Takazudo/zudo-osc-hole-field/project/osc-hole-field/handoff/README.md

# zudo-osc-hole-field R21

Start with **START_HERE.md** and **LOCAL_AGENT_PROMPT.md**.

This package completes the requested two SLEW controls on the existing grid and supplies a safe project-content overlay for the official zudo-circuit-doc initializer/runtime. It contains the working flat/3D preview sources, diagrams/print proofs, 45 authored MDX pages, 22 component research records, source acquisition queue, block/board contracts, decision log, KiCad sheet plan and engineering gates.

It is not a completed circuit, validated assembly, manufacturing BOM or fabrication release. Downloaded-source evidence, official runtime checks and hardware qualification are not inferred from software preview tests.
