Takazudo/zudo-osc-hole-field/research/osc-hole-field/planning-exploration/README.md

# Planning-time exploration reports

These nine reports are planning-time research dated 2026-09-28. They are preserved as source records and are not published on the documentation site. Some reports retain former project names and paths as historical planning context; those references do not describe the current project identity. See [rename provenance](../../../project/osc-hole-field/handoff/rename-provenance.json) for the recorded rename.
