Takazudo/zudo-osc-hole-field/design/spec/modules/fixtures/README.md

# Runner regression fixture

`envelope-ar-trace-control.txt` contains 13 selected rows from the retained ideal-model AR linear normal trace. It is an I/O acceptance control, not measured hardware data. Selection keeps the initial/final rows, maximum envelope and both sides of every stage transition.

Source: `.circuit-cache/envelope-spice/envelope-ar-linear-normal.txt`, generated by the pinned ngspice wrapper. Row indices below are zero-based data rows (header excluded).

```json
{
  "source_sha256": "59e285b6f2852b22980d5d8fd4fd9a8d9bdcaa34c83321e640de46be70bafdd8",
  "source_rows": 155734,
  "selected_rows": [
    0,
    13208,
    13209,
    24655,
    24664,
    24665,
    36610,
    36611,
    36617,
    36618,
    41326,
    41327,
    155733
  ],
  "scope": "Decimated retained ideal-model trace for runner I/O regression; not hardware data"
}
```
