Takazudo/zudo-osc-hole-field/project/osc-hole-field/workbench/mechanical/README.md

See ../docs/MECHANICAL.md. Generated 3D records are package and mounting-plane proposals, not a routed PCB, validated connector stack or mechanical release.
