Takazudo/zudo-osc-hole-field/design/panel/native-review-work-note.md

# Current-source panel native review evidence

The issue #37 acceptance audit found that the retained DRC report and both PNG copies still came from the issue #20 board with five 6.3 mm octave holes. The board changed those apertures to 7 mm at `2b213e0`; later prose described a fresh review but kept the earlier artifact bytes. This continuation refreshes those artifacts without changing any board, project, parameter, lock or owner-art bytes.

The completed clean panel baseline (323 seconds), PR126 native 20-case suite and ownership probe, and exact-head aggregate/docs CI provide the preceding source baseline. A fresh pinned native readback confirms all 438 features and five 7 mm octave apertures. Native DRC with all severities reports zero violations/open items and no added exclusion. The direct KiCad top render was opened alongside the old image; the title, fixed layout, labels, brackets, divider and border remain intact. The published copy is byte-identical to the new native render. No image editor or fabrication exporter was used.

`boards/panel/reports/native-review.json` records the actual native commands, image/version, source/output SHA-256 and byte counts, and renderer state. The final complete native readback/DRC/opaque-render replay completed under the guard in 120 seconds with all seven inputs unchanged and the custom `.kicad_dru` file absent before and after. The receipt includes the wrapper and feature-check producer hashes; introducing an unrecorded custom-rule file is rejected. An earlier transparent export completed but its wrapper's requested-versus-actual pixel-size assertion failed; that assumption is not a physical panel requirement. The final receipt records the actual 2352 × 2216 native canvas separately from the requested 2384 × 2240 pixels. Failed attempts remain diagnostic evidence, not passed wrapper runs.

Panel regeneration now runs the read-only receipt verifier. It rejects changed board/project/parameter/lock/pin bytes, changed native/published artifacts, incomplete DRC scope, nonzero findings, weakened clearance floors, added exclusions, command/oracle drift or mismatched image copies. It never refreshes hashes. Nine portable mutation tests exercise those boundaries against the actual tracked canonical artifacts.

To refresh after an intentional source change, run the recorded `commands` through the pinned wrapper under the heavy guard, into fresh or cleared ignored output paths; check zero native findings and inspect the resulting image. Preserve and compare input hashes across execution, copy only those actual native outputs to the receipt's declared artifact paths, then generate a new receipt from those same bytes and rerun `python3 scripts/panel/check_review_receipt.py`. Merely recalculating receipt hashes without fresh oracle work is not an evidence refresh. Re-run aggregate regeneration and documentation checks before publication.

This closes the retained current-board evidence gap only. The panel remains an unvalidated draft; physical selector, optical, clip/support and manufacturing checks stay under #55/#64/#65. Electronic schematic parity is not applicable to this board-only panel. No order or fabrication output is produced.
