Takazudo/zudo-osc-hole-field/design/standard/master-documentation-freshness-work-note.md

# Master documentation freshness

Baseline regeneration passed235s with no tracked drift at main1dac536. Main38153f8 was then integrated before task edits; its changes are the separate unselected inverter study.

The retained power SVG still depicted DW254P-2X8-L0 rather than the current CN301/XB301 abstract raw/load boundary. Master and power ERC notes also used old240/POWER12 and pilot24-warning results as present-tense claims. Canonical regeneration now calls the full-master smoke check (without repeating source generation), including exact warning identities, native netlist parity and the complete master audit, then regenerates retained exports. The exporter rejects missing/orphan SVG views and PDF page-count mismatches against the source hierarchy. Existing timestamp normalization remains unchanged.

Authored corrections distinguish historical power/rail results from current requirements, repair the Python producer command and S&H reference rail, and explain that TI OPAx197 Final1.3 exists while the complete MULT circuit remains unmodeled. The OPA4197 evidence owner and retained12-case output report were inspected; no new component or hardware claim is made. No source envelope, warning suppression, circuit value or historical snapshot hash changes.

Seven focused master-audit/budget/MULT tests, component validation, shell syntax and invalid-mode rejection passed. Independent read-only review found no blocker. Initial CI36978859750 at source097832c performed fresh full-master ERC: zero errors and228 exact warning identities, complete pin/net parity and master audit (35 hierarchy instances,33 signal modules,5906 exported components,5049 nets,209 sensitive nets,438 UIDs). It exported14 SVGs and36 PDF pages, then failed overall on the expected tracked regeneration drift.

Artifact11214898527 was inspected and only12 generated export files applied. An unrelated native-fixture timestamp was excluded. All62 recorded producer inputs remained unchanged. Every SVG parses, the PDF opens with36 pages, and its power page plus power SVG show current CN301/XB301 with no old DW254 inlet. No native artifacts were hand-edited; normalization is the existing timestamp-only script. A second exact-source aggregate is pending to establish export byte reproducibility and final clean CI.

No new component, capacity, protection or physical qualification is claimed. Issues24/33/34 remain open until the batch passes and merges; circuit59 and physical57 remain open independently.
