Takazudo/zudo-osc-hole-field/design/power/reference-capacitance-work-note.md

# REF output C0G bank

This issue #59 continuation changes only C104–C106 in the isolated monitor/permit candidate to KEMET C1206C104F3GACTU: 100 nF ±1%, 25 V, C0G, 1206. Three capacitors remain directly between REF and AGND, so nominal capacitance stays 0.3 µF. The other six KEMET X7R bypasses, C109, canonical instrument components, current ceilings and all 438 fixed hardware centres are unchanged. The new inventory identity is not fitted to the instrument.

The exact manufacturer sheet generated 2026-10-02 and C1003_C0G dated 2025-02-20 are retained unmodified in the ignored source cache. Their hashes, direct URLs, exact physical/printed locators and minimal extracts are committed in owner evidence and the acquisition receipt. The family specifies no capacitance change with applied rated DC voltage or time and ±30 ppm/°C relative to +25 °C. It does not supply a full-temperature leakage bound: its insulation-resistance test uses rated voltage for 120 ±5 seconds at 25 °C. The conditional DC allocation therefore retains its zero-capacitor-leakage assumption.

At the stated component-temperature range −40…125 °C, the largest departure from the TCC reference is 100 °C. Combining the initial ±1% tolerance and ±0.3% temperature factor multiplicatively gives the exact bank interval **296.109–303.909 nF**. The new checker consumes frozen candidate/catalog/owner bytes, requires the exact identities and primary facts, checks all three REF/AGND connections, and requires the entire interval strictly inside REF34 section 6.5's **0.1–10 µF** stable-output-capacitor range. It rejects altered evidence, malformed arithmetic, changed topology and source mutation during calculation.

This admits the component capacitance-value interval only. It does not establish installed reference-loop stability, ESR/ESL, soldering/environmental effects, actual component temperature or physical fit. Post-environmental qualification limits in the family sheet have their own test conditions; they are not a blanket installed lifetime guarantee. The REF34 table's common **10 µF** accuracy/Iq/timing condition is still unmatched. Source slew, startup/shutdown, line/load cross conditions, the narrow reference-validity requirement, logic ICC and return/isolation behavior remain open.

The exact body maximum is 3.4 × 1.8 × 1.8 mm. A dedicated footprint uses the manufacturer's Table 3 Density B 1206 lands: pad centres x = ±1.50 mm, pad size 1.15 × 1.80 mm and minimum courtyard 4.70 × 2.30 mm. The body display uses the source maxima; it is not an exact terminal/seating model. Native checks independently transcribe these dimensions and include top/bottom rotation, an undersized-height mutation and a swapped-pad mutation. Existing 0603 and generic 1206 assets remain unchanged.

The fresh combined-main baseline passed guarded regeneration in 205 seconds without drift. Focused checker regressions and subsequent native, aggregate, documentation and exact-head CI results are recorded in the PR and external review log. No source-contract or qualification flag is promoted. Issue #59 remains open; nothing is orderable or authorized for energization by this change.
