Takazudo/zudo-osc-hole-field/design/power/monitor-permit-draft-work-note.md

# Native monitor/permit candidate

Status: **unselected, unvalidated draft; not orderable or energizable**.
The [source](monitor-permit-draft.json) captures a seven-package monitor/permit
circuit with a finite dummy load. Canonical instrument protection remains
unimplemented and issue #59 remains open.

## Captured circuit

The isolated project is in `schematic/candidates/monitor-permit/`. It contains
42 proposed physical components and an ideal test-supply declaration. That
declaration is not an inlet and KiCad omits it from the board netlist export.
The native check compares all 113 physical pins, values, footprints, complete
MPNs and manufacturers against the source. Its fresh pinned KiCad 10.0.6 run
currently has zero ERC errors and zero warnings. The
[native receipt](monitor-permit-native-report.json) lists the default checks
KiCad did not run; none of this establishes electrical performance or fit.

- TPS37044MJOFDDFRQ1 monitors +12 V and +5 V on its 0.8 V channels. Its spare
  0.4 V channel provides a coarse reference window using 7.25 kΩ over 1 kΩ.
  That channel has different accuracy and hysteresis rows. Its divider adds
  nominally 0.4 mA to the reference load.
- TLV9022DR uses the previously studied negative-rail resistor network.
  Both comparator outputs now veto REF_SENSE; detected negative faults pass
  through the supervisor reset timer. Only supervisor resets drive FAULT_N.
  See [retiming conditions](monitor-fault-retiming-work-note.md).
- REF3433TIDBVR supplies the sensing reference. Three nominal 100 nF output
  capacitors are captured as a draft choice. Their effective capacitance remains
  unestablished because the existing Murata source is unavailable.
- SN74LVC1G17DBVR U104 buffers FAULT_N into GOOD_FAST. A second package,
  U106, buffers DELAY_IN into PERMIT_CLK. R120/R121 are 10 kΩ, C109 is 10 nF,
  and R125 is a 100 kΩ passive bleed from DELAY_CAP to AGND. The nominal driven
  gain is 10/11 and time constant 90.91 µs; disconnected-drive decay is 1 ms
  with zero pin capacitance and zero leakage. No powered-off LOW is inferred.
- SN74LVC1G74DCTR clears Q through GOOD_FAST and clocks a high D after the
  illustrative delay. Its complementary output is explicitly unconnected.
  MMBT3904,215 drives the same 10 kΩ dummy load from +12 V through a 10 kΩ
  base resistor with a separate 100 kΩ base bleed. These loads do not represent
  the instrument's isolation drivers. C110 supplies the additional local bypass.

Directly connecting the latch reset to the pulled-up RC node would create a
slow CMOS input transition. The buffered reset avoids that topology error.
A short raw GOOD_FAST low pulse can still clear Q while the timing capacitor remains charged,
leaving no new clock edge after recovery. Automatic re-arm is not claimed.

## Evidence and CAD

The component-evidence catalog now includes 15 exact candidate identities,
marked not fitted to the instrument. Its manual inventory has 64 lines,
48 fitted and 16 not fitted/hand fitted, with no declared placement binding.
The isolated candidate's proposed population is separate from that instrument
population. Supplier allocation is unverified.

New owner records retain exact source hashes, pin functions, conditional limits
and open application gates. TI SN74LVC1G17DBVR (SCES351Y, October 2025) and
SN74LVC1G74DCTR (SCES794G, September 2021) have timing tables at 5 V ±0.5 V,
covering the candidate's normal supply range. Actual input edges, output slew,
loads and reset/clock sequencing remain unqualified. The DBV/DCT source range
is −40…125 °C; instrument environmental requirements are unchanged. The old HC
owner records remain available for their other instrument uses.

The source-driven candidate assets reuse an existing 1 kΩ symbol unchanged.
Three additional family footprints use pinned KiCad 10.0.0 imports and original
8.0.0 WRL models. The resistor gets a separate candidate footprint so the
instrument's existing resistor footprint is preserved. A dedicated TI_DCT0008A footprint uses the retained TI example: 1.1 × 0.4 mm
pads at x = ±1.9 mm and 0.65 mm pitch. Its provisional 3.1 × 3.1 × 1.3 mm
body display omits leads and seating; drawing body dimensions exclude mold
and interlead flash. Pads retain the example R0.05 mm corner radius. Per-part CAD receipts
record source files, transforms and hashes. Package-family previews do not prove
exact lead fit, seating, solderability or installed thermal behavior. The family
model URI follows the existing board-project directory convention; a future PCB
under this deeper candidate directory must receive a suitable project-relative
model path before any 3D assembly check.

## Verification of this checkpoint

Fresh KiCad 10.0.6 ERC and pin/identity checks pass for the revised capture.
The 64-line evidence contract and 92-symbol/44-footprint/111-receipt library
checks pass. Native display checks cover 18 cases and five rejected mutations.
Focused regression tests and 22 fresh passive RC runs pass. Aggregate replay,
documentation build and final source review are pending for this revision.
These checks do not establish installed electrical performance.

## Open gates

The conditional [behavioral diagnostics](monitor-permit-behavior-report.json)
reproduce latch-off and re-arm for forced short/long GOOD_FAST low pulses in an ideal single-pole
RC abstraction. They enumerate all six arrival/failure orders as Boolean rail
sequences, not device-level transient simulations. Control-power loss and
subsequent recovery remain UNKNOWN. Device propagation, input capacitance,
reference trajectories and stored-charge clamp behavior are not simulated.

The report also accounts for nominal resistor currents and capacitor charge,
including the released coarse-reference divider. The separate conditional DC
allocation includes source-table active currents and the clamped divider feed;
dynamic current and actual isolation loads remain unbounded.
Original auxiliary allowances and current limits are retained.

The coarse reference window cannot certify the earlier 3.29–3.31 V precision
assumption. The combined FAULT_N capacitance is not shown to match TPS37044's
10 pF detection-delay test. TLV maximum delay/cold negative-input leakage,
reference startup/slow-slew behavior and effective bypass, LVC partial-power
behavior, and the NPN's passive-base turn-off bound remain open. A 100 kΩ bleed
does not reproduce the transistor's −1 mA reverse-base switching test.

Independent inlet-return/local-GND validity and the actual 82 output, 16 sense
and 30 reference isolation paths are outside this dummy-load capture. Installed
mechanical, thermal, as-built and bench qualification remain **NOT RUN**.
