Takazudo/zudo-osc-hole-field/design/power/precision-output-cell-connectivity.txt

GENERATED by scripts/checks/precision_output_cell.py
CANDIDATE ANALOG CELL; NOT SELECTED, NOT IMPLEMENTED, NOT ENERGIZABLE
Pin connectivity only; not a KiCad schematic, netlist receipt or fabrication input.

U1 OPA4197IPWR
  1: DRIVE
  2: FB
  3: SIGNAL
  4: VP
  5: GND
  6: SPARE_B
  7: SPARE_B
  8: SPARE_C
  9: SPARE_C
  10: GND
  11: VN
  12: GND
  13: SPARE_D
  14: SPARE_D
K_DRIVE AQY232G3HSX
  1: PERMIT_I_PLUS
  2: LED_MID
  3: DRIVE
  4: SW_DRIVE
K_SENSE AQY232G3HSX
  1: LED_MID
  2: PERMIT_I_MINUS
  3: SENSE_LIMITED
  4: FB
R_ISO_A RC1210FR-07499RL
  1: SW_DRIVE
  2: ISO_MID
R_ISO_B RC1210FR-07499RL
  1: ISO_MID
  2: JACK
R_SENSE RC1210FR-074K99L
  1: JACK
  2: SENSE_LIMITED
R_LOCAL RC0805FR-0710ML
  1: DRIVE
  2: FB
C_LOCAL C0805C103J5GACTU
  1: DRIVE
  2: FB
R_BLEED_P RC0805FR-07100KL
  1: VP
  2: GND
R_BLEED_N RC0805FR-07100KL
  1: VN
  2: GND

Permit driver, supply decoupling and board integration are OPEN; see source spec.
