Takazudo/zudo-osc-hole-field/design/power/WORK-NOTE-59.md

# Issue 59 — continuous contract and candidate evidence batch

Scope: correct the stale protection-audit continuous currents, retain exact candidate evidence, and choose the next complete cell. No protection circuit is selected/installed; issue 59 remains OPEN and the boundary NON-ORDERABLE / NOT-ENERGIZABLE. All 33 modules, 438 centres, source envelopes, precision targets and powered-off patching remain in scope.

Baseline at `79d9d4f`: `pnpm circuit:check` passed (49 manual lines, zero declared placements; pin-asset check performed; no schematic/placement binding). The 27 focused protection/supply tests passed. Mandatory aggregate regeneration ran through the machine-wide heavy guard after queueing, exited 0 with verdict PASS, and produced no tracked drift. Its native exports/ERC used the pinned wrapper: 10 boards, zero ERC errors and 673 retained warnings; this does not establish protection or physical qualification.

Changes: add declared `source_requirement.minimum_continuous_current_mA` of 1700/1600/300, consume it in the protection audit, and require equality to the independent ledger calculation in the supply generator. Preserve maximum delivered 2100/2000/500 and the original 40 mV drop. Regenerate resistance/PTC/FET screens. Count the existing 110 ADG quads directly from circuit-spec designators; record an unbooked TMUX sensitivity with 45 new local quads. Add the approximately 0.303 W per 499 ohm contention screen and explicit local-ground/thermal open gates.

Evidence: inspect actual TI TMUX741xF SCDS404B and LM7480 SNOSDD8 bytes and retain them in the ignored development cache. Commit exact order identities, hashes, minimal extracts, package/pin/drawing locators and stated conditions in `protection59-sources.json`. Actual final-page notices restrict reproduction/display, so no new PDF archive or public download is committed; cache absence is reported as NOT RUN for byte verification. Visually inspected TMUX printed pages 7/8 and LM7480 printed page 6 to distinguish typical/max columns. TMUX floating leakage is typical and its current table is conditioned at +/-16.5 V; no guaranteed +/-12 V project saving is asserted. LTC4371IMS#PBF official byte reads timed out at the canonical URL and `?download=1`; record SOURCE UNAVAILABLE, null file and zero hash. No guessed supplier code, inventory addition, publication selection or footprint substitution.

Next complete design: one precision-output protection cell with paired source-facing channels, jack-side current limiting, permanent local feedback, local all-rail inhibit and actual rail/control interfaces; cover reference receiver partial-power in the fault matrix. Actual passives/clamps, switch trajectories, local-GND loss, independent return diagnosis and the three-rail controller/discharge circuit remain open. Source/thermal/fit/fault-injection bench work is NOT RUN in issue 57, and cannot substitute for missing circuit design.

Source epoch: supply input/report and protection audit/script are members of the issue-54 snapshot file set. This batch changes those source bytes; no historical native/electrical receipt, snapshot or board source epoch is rebound. No board geometry, partition, routing solver input, schematic cell, inlet pin map or fitted package is changed. The manager must keep prior receipts historical and run any required aggregate checks after merging.

Final verification: 33 focused protection/supply tests PASS; protection and supply generated-report checks PASS; draft-contract gate exits 0 and implementation gate deliberately exits 1. `pnpm circuit:generate` writes zero component pages, `pnpm circuit:check` and `pnpm check` PASS. Foreground review added rejection of an accidentally promoted or negative-current candidate screen, retained explicit LM7480 test conditions, and moved TI bytes to development-only cache after inspecting the reproduction notice. Cache-absence/corruption regression coverage keeps portable checks honest. Full post-change native/build/site/browser runs are NOT RUN by this worker; the manager owns merged verification, and no new circuit or layout exists to qualify. The external completion review log records exact source-epoch hashes and the final commit.
