Takazudo/zudo-osc-hole-field/design/partition/core-model-scope.md

# K coupling diagnostic scope

## Current complete nominal K basis

The v7 pinned native prerequisite has the same 13,698 item UUID geometries,
499 holes and 59 zones as v6. The complete fitted AGND source set is 1,903
own loads, 376 GH returns and nine main lands, or 2,288 distinct contacts.
Eight extra source-DNP AGND pads remain native copper but carry no fitted
nominal injection. `core_full_ground_inventory.py` binds this set to the v7
native receipt. `core_model_entry.py` admits it only with all loads,
nineteen-support main profiles and no port limit. The guarded, source-bound
`preflight_core_full_ground.py` v3 extracted all 2,288 finite contacts from
the current geometry and formed 2,287 independent balanced functions over
219 physical barrel records. The v3 receipt binds the extraction/profile code
closure, contact proposal, nominal resistivity and an ordered support digest.
This is a **nominal extraction preflight only**: the complete matrix, physical
source flux/contact class, manufacturing/material interval, joined J/P/K
current allocation and electrical limits remain OPEN.

The successful v6 native prerequisite retains 3594 fixed source footprints,
1903 fitted AGND contacts, 188 main-array vias and 104 named header stitches.
All fitted AGND contacts, all 206 selected J-facing GH contacts, all nine AGND
main lands and all 104 stitches are in the main native AGND component. Native
rule and schematic parity errors are zero. The 551 warnings and 7354 complete
named open edges remain a ground-conductor prerequisite, not a routed K board.
The unchanged physical pad geometry, net, face and position comparison is exact.

`solve_conductor_volume.py` requires the actual successful native receipt and
generated source manifest for every `osc-core` input. It verifies all original
source, board, schematic, rules, project, native-export and DRC dependencies
before extraction and again before publishing a result. Failed populated exports
and a missing or mismatched receipt are rejected before meshing. The profile and
cache identities retain the complete prerequisite, including the 1903-contact
source mapping. Selecting coupling ports never sets K own-load currents to zero.

## Initial bounded computation

The initial diagnostic uses exactly 215 selected physical F-side contacts:
206 GH contacts and nine main lands. The first sorted main is the reference,
giving 214 independent profiles. Each GH profile is the existing fixed 0.25 mm
square numerical support. Each main profile uses nineteen equal finite supports
within its actual land, with total current one and current 1/19 per support.
This option changes each main functional, not the number of independent profiles.
The potential witness is restricted to a constant over the complete possible
4 x 4 mm wetting support and tied array ports. This is an admissible trial
restriction, not a physical ideal-pad or equal-sharing claim.

Initial mesh parameters are 2 mm bulk, 0.25 mm local regions, origin (0,0),
adaptive grading and barrel refinement 1. All four foils, actual holes and
foreign-net exclusions remain in the operator. The serialized heavy guard uses
one slot, a 3600 second run bound and a 6000 MB start-memory requirement.
Observed memory and actual residuals will be retained. All independent equation,
source, shared-face and barrel gates remain 1e-8 A; numerical energy allowances
are charged. No failed run or stale output stem can supply a result.

The matrix will quantify finite-profile common-transfer and private-access
feasibility, including all actual sheet spreading and shared barrel geometry.
No parallel-sharing factor is inferred from the extra stitches. A useful positive
K allocation must be supported by the joined J/K operator and unchanged 0.5 mOhm
common-ground ceiling. Four JL utility returns additionally need P/rest-network
coverage. K own-load injections, manufacturing/material bounds, real GH/load
contacts, full wire traces and signed current conditions remain unresolved.
Refinement and actual source acceptance follow only after the initial intervals
identify the dominant physical or numerical costs.

## Completed full nominal checkpoint — 1 October 2026

The recovered v7 full-basis calculation completed all 2,287 current and potential
functions, including the 1,903 fitted own contacts, 376 GH returns and nine main
lands. The guard recorded PASS/exit 0 after 7,048 seconds. The read-only receipt
audit and exact hashes are in `core-nominal-checkpoint-20261001.json`: all 44
model and 82 native prerequisite dependencies matched current bytes; both paired
matrices are finite and exactly symmetric. No independent residual recomputation
or eigensolve was performed in the audit. The earlier future-tense initial-basis
sections above describe historical stages, not the current completion status.

This completes nominal coverage for this exact candidate/source epoch only.
Physical contact/material/current classes, joined allocation and electrical
acceptance remain OPEN. No canonical K board is selected or accepted by this
result, and the largest self upper includes access terms rather than proving a
common-ground allocation.
