Takazudo/zudo-osc-hole-field/scripts/pcbgen/numerical-requirements.txt

# Reproducible draft ground-resistance extraction and numerical benchmarks.
numpy==2.2.6
scipy==1.15.3
shapely==2.1.2
