Takazudo/zudo-osc-hole-field/design/mechanical/WORK-NOTE.md

# Panel control evidence work note

Issue #12 covers the Bourns PTV09A-4020F B103/B104/B504 family and Alps Alpine SRBV160803 octave selector. The fixed R21 shaft positions come from `design/grid/placements.lock.json`; no positions changed. `design/standard/electrical-standard.json` OSC-ES-1 selects 51 B103, 48 B104, and two B504 roles by UID. B104 current sourcing and assembly availability remain UNVERIFIED.

The retained Bourns PTV09 family PDF (rev. 01/25) and Alps SRBV catalogue (update 2510) are in `sources/` with SHA-256s in each owner bundle and CAD receipt. The Bourns PTV09A-4 drawing is explicitly horizontal/rear mount and bushingless. Its 20 mm `L` shaft dimension is **not** a qualified PCB-to-tip installed height. The common footprint uses the horizontal/rear family recommended PCB hole layout; mounting-leg transfer to the exact -4 body and panel reach remain physical checks. All 3D WRLs are coarse body envelopes, not exact vendor models.

The Alps Drawing No.7 gives ten electrical terminals: 1 and 10 common, 2–7 positions, 8/9 dummy, plus two mounting features. Its Ø2 dimensions describe PCB bores, **not solid leg diameters**. The old same-orientation bores overlap at 17 mm pitch; this alone does not establish solid-leg collision. Issue #47 re-inspected the 18.2 mm support span and asymmetric body. The selected conditional draft uses 0/180 degree bodies on five independent adapters in two planes (3 at z=-16 mm, 2 at z=-29 mm), retaining all legs and original copper pads. See `selector-assembly.json` and the authored selector assembly decision. Physical qualification remains **NOT RUN**, tracked in [issue #55](https://github.com/Takazudo/zudo-osc-hole-field/issues/55).

The pin maps bind symbol pins to footprint pads; board nets are `UNASSIGNED` until circuit capture. The manual inventory has zero declared schematic placements and does not verify population. Source drawings, generated previews, and DRC fixtures were reviewed; no physical sample or panel stack was tested. All CAD is an unvalidated draft.
