Takazudo/zudo-osc-hole-field/design/partition/downstream-handoff-35.md

# Exact downstream issue amendments after #35

**Historical nine-board handoff. Issue #66 supersedes J topology, counts and affected interfaces; use `downstream-handoff-66.md` and the current manifest.**

These blocks replace the named issue's Goal/Board group text. Append the common contract to each issue, retaining unrelated original verification duties. Manager applies the shared GitHub edits after merging this branch. No remote issue was edited by the worker.

## Common contract for #36–#43

Authority: **PROPOSAL (planning, owner-delegated)**. Consume `design/partition/partition.json`, `partition-input.json`, `floorplan-candidate.json`, `loom-candidate.json`, `mechanical-candidate.json` and the exact generated `design/boards/osc-*.json` definitions. Every schematic/PCB is an **unvalidated draft**. All 33 modules and 438 UID x/y centres remain fixed; do not shrink footprints, move hardware or split a Sensitive island/package to make a board fit. J's mixed-face placement stays on one physical board. If actual placement/routing or deterministic geometry overflows, amend the partition sources and remaining tasks, regenerate affected artifacts and repeat joined net parity.

One EXT conditional domain remains selected. Source and orderable inlet/mate are NOT SELECTED. `CN301`/`XB301` are audit-only AbstractBoundary components: no physical footprint, BOM part or invented conductive bridge. Preserve inlet/support/cable reservation x260–308/y248–293/z−85…−45 mm. Minimum continuous +12/−12/+5 requirements are 1700/1600/300 mA; transient 2000/1900/400 mA; maximum delivered envelope 2100/2000/500 mA, with 4.6 A worst single return. These are requirements, not measured capacity.

The exact internal GH families are JST BM03B/BM07B/BM08B-GHS-TBT(LF)(SN) top-entry headers, GHR-03V-S/GHR-07V-S/GHR-08V-S housings and SSHL-002T-P0.2 contacts. Use #63 source footprints and manufacturer numbering. The 7.3 mm mated height is a reference at each board face, not a rigid inter-board separation. K/P GH3 headers use source clockwise rotations P=90 degrees and K=270 degrees; the other K mates use 180 degrees opposite B-side source 0 degrees. Use the explicit `kicad_orientation_deg` fields: raw KiCad flip/angle conventions differ. Four J/P GH3 loops remain at source 0 degrees. The 195 harnesses use source pin maps and retained Alpha Wire 6821 AWG26 evidence; maximum proposed cut is 204 mm, every source-driver aggregate remains <=1 nF/300 mm. The provisional current derating is 0.5 A/contact against the manufacturer 1 A at AWG26; assembled heat/crimp qualification remains NOT RUN.

There are 390 headers, 1,830 header positions, 513 signal conductors, 380 AGND conductors, 18 GH rail conductors, and four unwired positions across the entire harness set at each end. Do not fit crimps into NC positions. Two mechanical pads per header are retained unnetted; external housings/crimps are assembly items, never PCB footprints. Connector friction and solder joints carry no operating or harness-pull load.

Twelve factory-soldered Alpha Wire 5859 AWG14 wires and 24 custom 4×4 mm PCB copper terminals connect existing regulated load-side nets between K and J/P. They do not energize or cross the abstract source boundary. Use exact terminal coordinates and net names in the partition. The 125 mm wire ceiling, hot resistance <=13 mΩ/m, combined termination <=0.2 mΩ, rail plane <=1 mΩ and AGND plane <=0.5 mΩ yield 16.628 mV worst distribution loss including 4.6 A shared AGND displacement, below 20 mV. These are acceptance constraints awaiting actual layout/hot measurement; preserve the complete <=0.20 V source/rail/return budget and separate source-inlet 20 AWG contract.

Normal all-mates-present GH return bounds use conductance extrema with three independent AWG14 AGND wires per J/P, not equal sharing: J <=0.443 A and P <=0.492 A per contact. The complete combined J-or-P plus K PCB AGND spreading/neck resistance must be <=0.5 mΩ, including vias. The calculation conservatively adds that common resistance to all alternative return paths while giving the candidate GH path zero PCB/contact resistance. #38/#39/#43 must extract and #65 must hot-measure this routing limit; it is not a layout-independent measured value. Alpha 6821 wire resistance must remain >=0.1 Ω/m and <=0.17 Ω/m across the qualified temperature envelope; the lower bound is an acceptance requirement, not manufacturer guaranteed. Cold qualification remains NOT RUN. P has only 8.125 mA margin to the 0.5 A limit: this is a tight conditional routing requirement, not measured margin. If the actual hot AGND neck fails the limit, revise the lands/returns. The four J/P utility returns are separately bounded at 0.250 A. Main-return-open, partial mating and patch-sleeve/external-ground faults remain OPEN. EL's rail contracts are 50/50/70 mA with <=170 mA absolute return; six rail paths and twelve AGND paths need their real resistance bounds, not equal-current assumptions.

Four powered boards J/P/K/EL reserve 4.7 µF per rail each, with 12 finite 5×3 mm courtyard slots (EL height<=1.75 mm, others<=5 mm), all checked against current hardware/headers/service holes. Exact parts may require a source/partition replan; no footprint shrink or fitted zero-area placeholder is permitted; current fitted plus new board bulk is 68.7/61.5/43.3 µF nominal from the generated supply report, within 150/150/100 µF. Recompute after additions, retain +20%/≥10 ms ramp, and do not invent zero-area protection or bulk components. All existing source load ledger entries stay counted once.

Persistent gates: #65 main J/P/K/EL seated datums, support/carrier/comb strength, 195 GH looms and twelve load wires, service tool/latch sequence, hot resistance and proposed ≥120 mm inner enclosure depth; #55 selected 3+2 selector coupon; #57 source/inlet realization; #64 optical/hot indicator qualification. Exact protection remains OPEN #59 for 82 output, 16 precision-sense and 30 octave-receiver obligations. Unavailable physical checks are **NOT RUN**. No fabrication order files, supplier contact or owner soldering.

## #36 — replacement Goal and implementation scope

Generate nine per-board schematic projects: `osc-jack`, `osc-control`, `osc-stage-optical`, `osc-core`, and `osc-octave-1` through `osc-octave-5`. Project the complete per-reference assignment from the current native master: 5,904 physical rows including eight DNP, 5,896 fitted parts and 650 fitted ICs. Keep `CN301`/`XB301` as audit-only boundaries and do not infer load-side continuity through them.

Insert the 390 exact GH headers with their stable `pcb_reference`, manufacturer pin numbers, mechanical-pad exceptions and pin maps. Treat 390 housings and 1,822 fitted crimps as external assembly items. Project 24 custom load-side solder terminals (TP990001 onward) and join the twelve specified factory wires as declared interfaces; no orderable power-inlet part is introduced. Keep reserved future board bulk/protection explicit until #59 selects exact circuits/parts. Prove that joining every declared signal, return and load-side wire recovers exactly the master nets while preserving the abstract source break and all local Sensitive islands. No raw TIP, storage or summing node may cross.

Export `schematic/boards/<board-id>.net` and `.kicad_sch` paths named by the definitions. Carry `BoardSide` and the explicit `kicad_orientation_deg` from the floorplan/connector maps. Source rotations are clockwise after B-side X reflection. The pinned in-memory oracle checks every used footprint/side/rotation class. Native cached courtyards add0.045 mm per edge; source free-placement margins are0.35 mm between drawn courtyards and 0.30 mm at edges, covering a 0.05 mm per-edge inflation ceiling. Do not attempt to represent a whole J module with one face-only cluster: #38 must support the selected mixed-face map. Re-run native parity/ERC and provide the actual graph/contact/component counts, not a hand-counted approximation.

## #37 — replacement Goal and panel handoff

Regenerate the flat 318×298×2 mm panel from current geometry/panel parameters, preserving all 438 x/y centres and owner artwork. Control domains are consolidated to P, octave hardware remains O and 12 stage LEDs are EL. J remains the jack/102-indicator domain. Apertures remain conditional: jack6.2, pot6.3, toggle5.2, button5.0, octave shaft-only7.0 mm; 1.6 mm bare-FR4 mask-open indicator windows remain a proposal, not optical qualification.

**The 35 EL support holes are internal PCB holes, not front-panel drills.** Thirty also require internal P clearances; five top posts are outside P. J8/P6/K8 edge support holes and K191 Ø2.2 service-tool apertures are likewise internal. The decided front support drill count is zero. Check the proposed captured enclosure perimeter lip/clips at the 0–3 mm border against artwork, copper, existing hardware/nut/shaft apertures and assembly tools. Do not silently add a 35-hole front fastener pattern. P is x1–317 with support collars centred x3.5/314.5; check its projected edge setback while preserving the panel face geometry.

Keep the original 3+2 selector carrier/shaft apertures and the conditional EXT pocket. Report any deterministic artwork/support conflict with dimensions and revise partition sources before fabrication. #65/#55/#57/#64 seated/strength/source/optical qualifications remain NOT RUN.

## #38 — replacement Board group and scope

One board: **`osc-jack`**, outline (4, 20), (314, 20), (314,164), (4,164) mm; F.Cu faces panel at proposed z=−10 mm. Four layers, 1.6 mm, 2 oz; inner AGND and regulated-rail planes. Single-board Standard PCBA size envelope is satisfied by 310×144 mm.

Own all 180 jacks, 102 current compact LEDs and every J-assigned local input/output/protection circuit. There are 2,091 assigned master packages. Consume the exact per-reference F/B courtyard proposal; J needs mixed faces. Implement a narrow placer extension allowing explicitly selected per-reference faces within one module cluster, preserving every physical IC, local Sensitive island and bypass relationship. Keep through-hole copper/tail exclusions on both faces, maintain local decoupling/return paths and account for added vias. Neither the former rear-face overflow nor raw courtyard area is a routed-placement pass.

Place 52 GH8 and four GH3 rear headers at the source sites (56 total), eight edge M2 supports with Ø2.2 holes/3.2 mm collars, and six load-side power lands (+12 V, −12 V, +5 V and three separate AGND wires). Verify the combined J+K AGND spreading/neck limit <=0.5 mΩ. Preserve the B-face future output/sense protection reservation x120–310/y143–161 while subtracting actual hardware pads and power lands; unknown #59 geometry is not assumed to fit for free. The 0.35 mm compact-LED/jack nominal courtyard gap is drawing-derived; nut/shoulder seated fit remains #65. Jack bushings and nuts clamp directly to the panel. All 82 output/16 precision-sense protection obligations remain represented.

## #39 — replacement Goal and Board group

This issue now owns **all consolidated controls**, plus the five selected octave adapters. Do not restrict it to the original five oscillator columns. Implement `osc-control` and `osc-octave-1` through `osc-octave-5`; #40/#41 verify their no-op reassignment and #42 owns only the separate stage-optical board.

**`osc-control` / P:** outline (1,194), (94,194), (94,176), (317,176), (317,292), (1,292) mm; F.Cu proposed z=−11.8 mm, four layers/1.6 mm/2 oz. Own all 101 pots, 30 toggles, eight buttons and all 146 free control/slew parts (285 master packages total). Both SLEW pots, complete local high-impedance networks and required buffers remain together on P. All H/AB, filter/mixer/folder and envelope/offset controls are included. Reserve six load-side lands (three rails plus three independent AGND wires) and verify the combined P+K AGND spreading/neck limit <=0.5 mΩ. Retain exact B3F-1020 buttons with proposed captive 7.8 mm guided plungers; actual stroke/seating is NOT RUN.

P has 127 GH3 rear headers:123 K/P ports at source 90 degrees and 4 J/P ports at source 0 degrees, six main M2 supports at x3.5/314.5 and y196.5/238/289.5, 30 internal optical-post clearances and four factory load-side power lands. Its 316 mm width is required to clear the original pot courtyards; do not shrink it back to x4–314 or move hardware. Bushingless-pot/button body carriers and enclosure-side rails react user loads independently of solder. All post coordinates, collars, control passages and inlet-avoiding free header sites come from the partition.

**Five O adapters:** each keeps the selected 19.8×21 mm rectangle centred on its original shaft (x14.5, 31.5, 48.5, 65.5, 82.5; y185), with 6 mm wide top tongue to y171. O1/O3/O5 F.Cu z=−16; O2/O4 z=−29 with selected 180-degree switch rotation. Two layers/1.6 mm/1 oz, one original selector and two GH7 rear headers per board. GH7 mounting-copper gap is 0.35 mm; GH8 overlaps0.27 mm and is forbidden here. Source front body interval0…+7.5 mm is separate from rear terminal reach−4…0; check the exact rear pad/tail projections against the headers without inferring solid-leg dimensions from bore diameters. Preserve M9 stepped carrier, tongues, two extensions, five knobs and pin indexing.

Use a proposed factory carrier/handling panel of at least70×70 and at most250×250 mm for each small adapter; demonstrate tooling/rail removal without cutting retained selector pads/tongues. No final fabrication panel or order files in this draft. Installed adapter/tail/solder/service fit stays NOT RUN #55/#65.

## #40 — replacement Goal and Board group

**SKIP:** All 50 filter/mixer/folder pots and their complete assigned control islands are reassigned to `osc-control` under #39; this group has no independent board.

Verify this no-op against the regenerated master/partition: every original MP hardware UID and every assigned control package must appear exactly once on P, while the corresponding complete core circuits remain on K and jack interfaces on J as explicitly assigned. Verify no omitted module, duplicate PCB, lost Sensitive island, or obsolete MP board definition/netlist. Record the checked reassignment before closing; do not draw an empty board or silently discard circuitry. The common conditional EXT/protection/qualification contract still applies.

## #41 — replacement Goal and Board group

**SKIP:** Both SAMPLE buttons, both A/B toggles, both SLEW pots and their complete control/slew islands are reassigned to `osc-control` under #39; this group has no independent board.

Verify this no-op against the master/partition and both SLEW_STORAGE closures. Each SLEW pot, 2.2 kΩ/500 kΩ network, five C0G capacitors and local buffers stays on P; only the declared buffered interfaces cross. Verify no omitted utility module or obsolete UT/US/UP board. The hold cores remain on K and raw jack interfaces on J exactly as assigned. Record the reassignment proof before closing; no empty board is generated.

## #42 — replacement Goal and Board group

One board: **`osc-stage-optical` / EL**, rectangle (210,164), (317,164), (317,277), (210,277) mm. F.Cu proposed z=−4.2 mm, thickness0.4 mm, two layers/1 oz, double-sided Standard PCBA/ENIG proposal. This issue owns all 138 complete stage-circuit parts, including 12 current Kingbright emitters, 12 source 1.2 kΩ limiters, whole dedicated driver packages and their bypasses. Envelope/offset pots, toggles andbuttons are reassigned to P/#39; do not create ES/ET/EP duplicates.

Consume the 42 exact passage centres:18 toggles atØ11, 6 guided buttons atØ9.5 and 18 shaft passages atØ6.3 (including 6 offsetATTEN shafts). Holes>=6.3 are routed in the proposed assembly process. Retain 35 Ø2.2 internal support holes at the supplied 5×7 coordinate grid, 3.2 mm front collars andØ2 posts terminating in the control/body carrier. Six GH8 rear headers sit atx218.5+17n, y172; all 6 looms reach K and carry the explicit 3 signals/2AGND/3rails maps. No front-panel support drill pattern is implied.

The nominal front component/panel gap is0.45 mm; the rear gap is0.4 mm only with nonpassing pot-body front<=−5 mm. Keep the thin-board support/stiffness/tolerance requirement OPEN #65. The two-layer exception requires complete local LED loops, continuous rear AGND where unperforated and careful return stitching; actual routing may not use apertures or support holes. Factory backup tooling is required during GH mating; source wire combs take strain. Optical/brightness/hot resistor/LED behavior remains NOT RUN #64.

## #43 — replacement Goal and Board group

One distinct rear core: **`osc-core` / K**, polygon (4, 8), (314, 8), (314,246), (258,246), (258,292), (4,292) mm; F.Cu proposed z=−100 mm, four layers/1.6 mm/2 oz, no panel hardware. Own 3,385 master rows including 8 DNP (3,377 fitted), all complete source-assigned rear core/reference circuits and the conditional existing load-side star. D09 still requires this rear core; it is not SKIP.

Place the 191 F.Cu GH headers at the exact source sites:123 GH3, 58 GH8 and 10 GH7. Use source 270 degrees for its 123 GH3 K/P mates and 180 degrees for its 58 GH8/10 GH7 mates; explicit native KiCad angles and footprint origins are in the manifest. Preserve all 191 Ø2.2 service apertures and checked 1.5 mm hook approaches, eight edge M2 supports, twelve factory load-side power lands (six per J/P branch; three independent AGND wires each), combined branch-board plus K AGND spreading/neck <=0.5 mΩ, and the source-defined future rail/30-octave-receiver protection reserve x180–256/y220–290 on B.Cu. Keep all current reference packages/bypasses and genuine #62 branch/source current bounds; do not restore the overloaded shared reference scheme.

The K B-face is−101.6 mm. A 5 mm rear component-height ceiling and proposed inner enclosure rear−120 leave13.4 mm nominal clearance. The full source inlet/support/cable reservation remains x260–308/y248–293/z−85…−45; its XY notch is retained even though K is deeper. Do not install rejected P+B trays or assign footprints to CN301/XB301. Internal soldered14 AWG load wires do not replace the separate20 AWG source-inlet contract.

Show unpowered disassembly: external source disconnected/discharged, rear cover and wire combs released, all K mates unlatched through service apertures before K support removal. Tool/latch ergonomics, tail/solder solids, carrier strength and case depth remain NOT RUN #65; exact energized protection/source work remains #59/#57.

## Epic summary comment text

Issue #35 records a conditional nine-board draft: J, unified P, complete EL optics, five 3+2 octave adapters and a distinct K rear core. All 438 panel centres/33 modules, 650 fitted ICs and exact 114 Kingbright LEDs are retained. Source/package/island assignment, 390 exact GH header sites, 195 controlled ribbon corridors and hot-load distribution arithmetic are checked; worst proposed board-distribution loss 16.628 mV. #36–#43 now use the concrete source manifest, with #40/#41 verified-reassignment SKIP tasks. No PCB is drawn or fabrication output produced by #35. Physical seated/support/loom/service/depth qualification remains NOT RUN #65/#55, source #57, optical/hot LEDs #64; exact82/16/30 protection obligations remain OPEN #59. CN301/XB301 remain nonphysical, nonorderable audit boundaries with no invented continuity.
