Takazudo/zudo-osc-hole-field/design/power/downstream-amendments-48.md

# Exact issue-body amendments after issue 48

The manager owns shared GitHub issue bodies and dependency graph updates. Replace #52's provisional Goal paragraph with the block below, preserving its working agreement and original deliverable/acceptance list. Append the #35 block after its selected selector input and remove conflicting present-tense requirements for internal P+B pockets. Retain the historical source comparison and original qualification requirements via #57.

## Issue 52 replacement Goal block

Implement the owner-delegated single-domain external regulated-source requirement in `design/power/supply-architecture-input.json` and generated `design/power/supply-architecture.json`. All 33 modules, OCTAVE_REF, 347 current-ledger worksheet loads and 634 fitted IC packages belong to EXT; the raw inlet nets are +12V_IN, -12V_IN, +5V_IN and the instrument rails remain +12V, -12V, +5V with common AGND. Regulated outputs are never paralleled. Preserve all 438 panel UIDs and sensitive local islands; derive hierarchy counts from the actual implementation.

Physical source and orderable inlet/mate/contacts are NOT SELECTED; energization is NOT AUTHORIZED. This task may produce conditional CAD using an explicitly requirement-only interface, but must not draw a guessed orderable footprint. `OSC-EXT-PWR-8-R1` uses logical pins 1:+12V_IN, 2:-12V_IN, 3:+5V_IN, 4:NC, 5–8:AGND. Before selecting an orderable header/mate/contact, retain exact manufacturer drawing, physical mating-face/pad map, simultaneous-contact current/temperature and voltage ratings, wire/crimp limits, promote the evidence/selection through the owner bundles, and reconcile the logical pin map. Molex 43045-0800 / 43025-0800 / 43030-0007 are unselected candidates only; blocked drawing downloads and unsupported application derating are recorded in `design/power/inlet-source-attempts.json`.

Required source delivery (+12/-12/+5 order): at least 1600/1500/300 mA continuous and 1900/1800/400 mA for at least 20 ms; source voltage magnitudes 12.00–12.30 / 12.00–12.20 / 5.05–5.10 V. Source/inlet limiting must also impose maximum delivered currents 2000/1900/500 mA including tolerance, then coordinated all-rail shutdown. These maxima are requirements, not known part ratings; prove transient/let-through bounds rather than treating minimum source delivery as a maximum fault current. Preserve load bands 11.53–12.48 / 11.74–12.37 / 4.81–5.20 V and <1 mVp-p ripple. Full rail plus return loss <=0.20 V; common return displacement can increase a rail magnitude, so check both band edges.

Require 5 A simultaneously loaded contact and conductor capability and >=30 V contact rating; each ground contact must tolerate the entire 4.4 A maximum sum without assuming equal sharing. Factory-crimped copper >=20 AWG, <=300 mm, hot wire resistance <=0.04 ohm/m, complete contact/crimp path <=0.008 ohm, protection drop <=40 mV, board distribution drop <=20 mV. Actual identities, temperature derating, crimp quality and contact fit remain evidence/qualification gates. Do not reuse the old 1.1 A inlet PTC at the new whole-instrument analog current. Reconcile protection loss/dissipation and all auxiliary loads with the explicit 20 mA per-rail allocation; missing evidence remains open.

Count all local decouplers, regulator/reference and board bulk within unchanged 150/150/100 uF nominal +20%, including 100 nF per supply pin and initial 4.7 uF per board/rail. Require monotonic ramp >=10 ms; the full-capacitance increments are 224.64/222.66/62.40 mA. Keep inlet bleeders and leakage, doubled S&H REF5050/logic allowances, NOISE2 sensitivity and the single external-output-fault term from the decision. No savings or guaranteed instrument maximum is booked. Recompute the requirement if actual implementation exceeds an allocation; do not weaken it or silently add source capacity.

Implement source-backed load-side three-rail monitors, inhibited input enables, reverse-current blocking and coordinated all-rail shutdown/discharge without depending on an upstream power-good pin. Bound any-order/missing-rail intervals and output/precision-sense/reference injection, including external patch +/-12 V while EXT is off. Source-facing ADG5412F inputs alone do not protect output paths; source reverse blocking alone does not prevent backfeeding the instrument. Keep all 180 sleeves on AGND and reference fanout within EXT; analyze unplugged receivers, return-open, shifted/reversed cable, brownout/hiccup and external earth loops. Live service/hot plugging is prohibited. Do not label an unimplemented protection requirement as a passing circuit.

Preserve the original single-source deficits, rejected two-source comparison and three-independent-source evaluation. Persistent qualification issue #57 retains all original source capacity, thermal, startup, 15 V-only programmed-state/readback, connector, capacitor, partial-power and fit requirements. Leave measured capacity and guaranteed whole-instrument maxima null. No hardware measurements, source orders, supplier contact or energization are authorized. Draft completion does not close #57.

## Issue 35 appended input block

<!-- supply-architecture-48:start -->
## Selected supply architecture input after issue 48

Consume `design/power/supply-architecture-input.json`, `design/power/supply-architecture.json` and `doc/src/content/docs/decisions/osc-supply-architecture.mdx`, together with #52's implemented conditional interface and #54's pre-partition confirmation. The selected topology is **one EXT domain from an external regulated-source requirement contract**. Physical source and orderable inlet/mate are NOT SELECTED; no source capacity or physical energization is authorized. Preserve all 33 modules, all 438 panel UIDs and sensitive local islands. The old one/two-source deficits and three-P+B evaluation remain comparison evidence; **do not install the three rejected P+B trays** or require an internal source pocket for this selected topology.

Reserve the inlet/mate/support/cable envelope x=260..308, y=248..293, z=-85..-45 mm (panel front z=0, rear negative). It requires an enclosure bracket and strain relief, a maximum 30x30x16 mm mating-pair body, and 15 mm latch/bend access; these are requirement-only dimensions, not sourced component geometry. Resolve the enclosure inside depth and support loads explicitly. Preserve the selector 3+2 adapter/rail reservations from #47/#55 and do not move front hardware. Any selected orderable connector footprint must follow retained exact primary drawing and rating evidence; otherwise mark the CAD interface REQUIREMENT ONLY / NOT ORDERABLE and do not claim an exact connector fit.

Pin/current/harness/rail-loss/source-envelope requirements are in the decision and #52. The inlet has one contact per regulated rail and four AGND contacts with explicit common patch-sleeve return paths; never infer equal contact sharing or isolated returns. Buffered reference/control wiring crosses boards only inside EXT and within OSC-ES-1 limits; timing, hold, integrator, summing and slew storage nets remain local. Count every board bulk/decoupler against unchanged 150/150/100 uF nominal +20% and the >=10 ms ramp. Review board-distribution loss <=20 mV alongside the complete <=0.20 V rail/return budget, including the sign of shared AGND displacement. The min continuous source requirement is 1600/1500/300 mA; transient 1900/1800/400 mA; maximum delivered-current envelope 2000/1900/500 mA. All are requirements, not measured capacity.

Issue #57 remains OPEN for physical source realization/capacity/thermal/startup/programming, exact installed connector/harness and power-off/fault/fit evidence. Its unavailable measurements do not prevent a conditional board draft; deterministic electrical or geometric failures must be repaired/replanned. Do not reduce a board group or module scope to meet these limits. Carry this actual topology and evidence boundary into #36–#43 body updates and all ten required board-pair interface fields.
<!-- supply-architecture-48:end -->
