Takazudo/zudo-osc-hole-field/boards/panel/reports/visual-review.md

# Issue #20 top-render review

Reference: R21 318 × 298 mm rendered proof attached to issue #20, inspected at full resolution. Target: `panel-top.png`, KiCad 10 top-side render with proposed black mask, white silk and exposed ENIG gold. Whole-board, oscillator jack group and envelope control columns were opened at close range.
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
