Takazudo/zudo-osc-hole-field/_temp-resource/1-osc-hole-field/handoff-r21/zudo-osc-playground-r21-handoff/payload/project/osc-playground/workbench/reports/pdf-proof.png

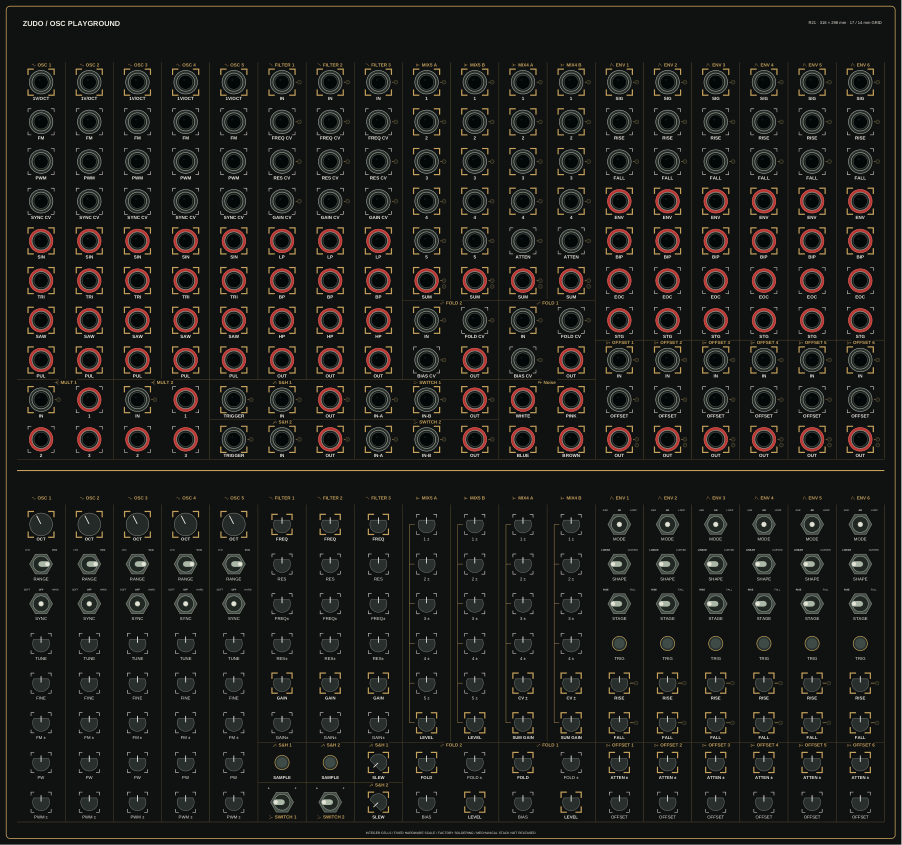
_temp-resource/1-osc-hole-field/handoff-r21/zudo-osc-playground-r21-handoff/payload/project/osc-playground/workbench/reports/pdf-proof.png
