Takazudo/zudo-osc-hole-field/design/mechanical/sources/alps-srbv-hardware.gif

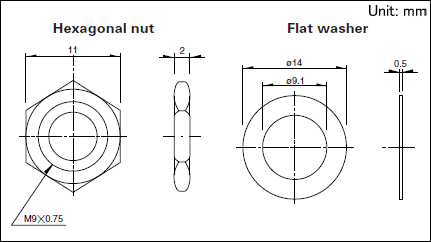
design/mechanical/sources/alps-srbv-hardware.gif
