Takazudo/zudo-osc-hole-field/design/mechanical/sources/alps-srbv-shaft.gif

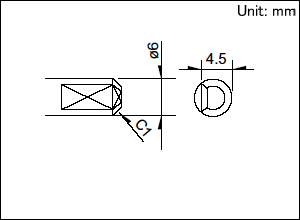
design/mechanical/sources/alps-srbv-shaft.gif
