Takazudo/zudo-osc-hole-field/project/osc-hole-field/workbench/reports/mobile.png

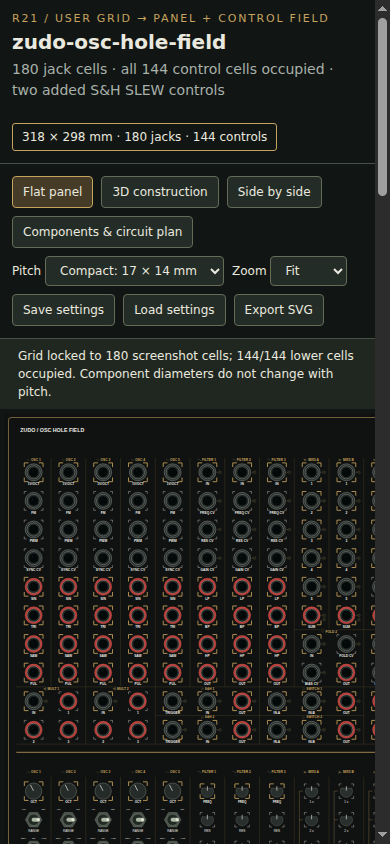
project/osc-hole-field/workbench/reports/mobile.png
