Takazudo/zudo-osc-hole-field/project/osc-hole-field/workbench/studies/screenshot-comparison.png

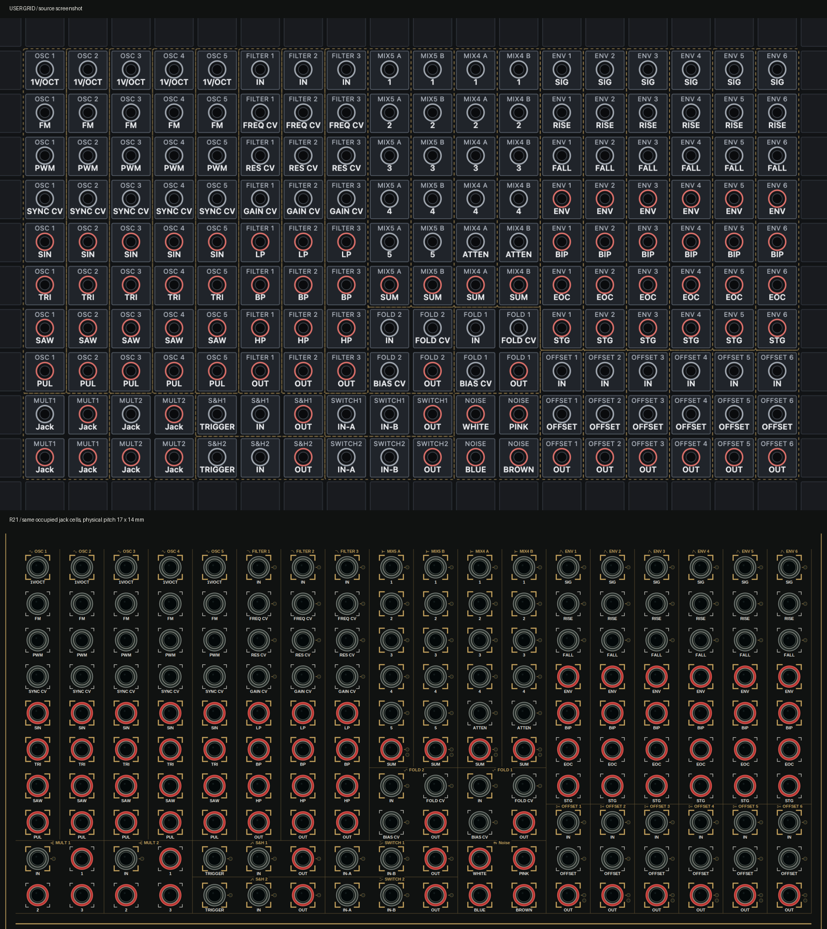
project/osc-hole-field/workbench/studies/screenshot-comparison.png
