Takazudo/zudo-osc-hole-field/circuit/routing/issue189/jl-u1502-component-joint/README.md

# Negative bounded joint screen

Full native cut components as terminals. Both saved variants failed to produce a complete transaction. Partial ground/signal rows are diagnostic only and must not be submitted or counted as accepted copper. Source/native-dump hashes, geometry, endpoints, diagnostics and exact timings are in result.json. Expansion cap remains300000; the heavy guard passed (15 combined with JRs). No native acceptance was run for these incomplete rows. Do not repeat this configuration unchanged or infer physical impossibility from this bounded search.
