Takazudo/zudo-osc-hole-field/doc/src/content/docs/components/integration/index.mdx

---
# GENERATED by @takazudo/zudo-circuit-doc — do not edit; run `zudo-circuit-doc generate`
title: "Integration"
description: "Cross-component rules — monitor-permit-startup, precision-feedback-physical-qualification — with the records and facts each spans, its conditioned calculations, and what it refuses to conclude."
sidebar_position: 4
---

Generated from the component evidence records — edit the records, not this page.

A component record answers questions about one part. These rules answer the ones that span several — whether a divider built from two resistors keeps a third part inside its own limit, whether a clamp event stays under everything downstream of it. Each rule is projected whole from stored evidence: its conditions, the exact facts it rests on, any conditioned arithmetic, and the exact wording of what it refuses to conclude.

## How to read these rules

- **The refusal is the rule.** — Every rule states, in its own words, what may NOT be concluded from the evidence above it. That sentence is the rule's real output; the verdict is shorthand for it.
- **A verdict belongs to the rule, not to a part.** — A rule's verdict says how far the cross-component question has been settled. It is never a judgement about any of the parts the rule names, and the verdicts are never combined into one.
- **Calculations are conditioned, and the conditions are the point.** — Each calculation publishes its expression, its inputs and the exact results that were recorded, together with the conditions under which the answer means anything. A result read without them is arithmetic mistaken for a measurement.
- **Numbers here were carried, not computed.** — The expressions are published so a reader can redo the arithmetic. This page does not evaluate them — the results shown are the ones the evidence recorded.
- **An evidence chain does not flow downhill.** — A stage being settled says nothing about any stage after it. A document confirming a limit is not a measurement of the assembled board.

## Rules at a glance

<EvidenceAnchor id="integration-index" />

<EvidenceTable label="rules-index">
  | Rule                                                                                      | Domain                                                    | Records | Facts | Verdict     |
  | ----------------------------------------------------------------------------------------- | --------------------------------------------------------- | ------- | ----- | ----------- |
  | [`monitor-permit-startup`](#monitor-permit-startup)                                       | unselected monitor/reference/latch startup and power loss | 6       | 6     | UNSOURCED   |
  | [`precision-feedback-physical-qualification`](#precision-feedback-physical-qualification) | precision-output feedback compensation and fault duty     | 2       | 6     | NEEDS BENCH |
</EvidenceTable>

## monitor-permit-startup

<EvidenceAnchor id="monitor-permit-startup" />

**Domain:** unselected monitor/reference/latch startup and power loss

**Verdict:** UNSOURCED

**This rule refuses to conclude:** Do not accept a complete permit or protection boundary from these partial component and draft-connectivity facts. Independent return integrity and physical qualification remain open.

**Conditions:** Six-package candidate only. Coarse reference validity, control-power loss, retained charge, latch timing and sink release need whole-circuit evidence.

**Records this rule spans:**

- [`rec-monitor-tps37044mjofddfrq1`](/docs/components/records/monitor-tps37044mjofddfrq1/) — TPS37044MJOFDDFRQ1
- [`rec-monitor-tlv9022dr`](/docs/components/records/monitor-tlv9022dr/) — TLV9022DR
- [`rec-monitor-ref3433tidbvr`](/docs/components/records/monitor-ref3433tidbvr/) — REF3433TIDBVR
- [`rec-schmitt`](/docs/components/records/schmitt/) — SN74HC14DR
- [`rec-flipflop`](/docs/components/records/flipflop/) — SN74HC74DR
- [`rec-npn`](/docs/components/records/npn/) — MMBT3904,215

**Facts this rule rests on:** each is published in full on the record page that owns it, at the anchor linked here.

- [`fact-monitor-tps37044mjofddfrq1-application-qualification`](/docs/components/records/monitor-tps37044mjofddfrq1/#fact-monitor-tps37044mjofddfrq1-application-qualification) on TPS37044MJOFDDFRQ1
- [`fact-monitor-tlv9022dr-application-qualification`](/docs/components/records/monitor-tlv9022dr/#fact-monitor-tlv9022dr-application-qualification) on TLV9022DR
- [`fact-monitor-ref3433tidbvr-application-qualification`](/docs/components/records/monitor-ref3433tidbvr/#fact-monitor-ref3433tidbvr-application-qualification) on REF3433TIDBVR
- [`fact-schmitt-electrical-limits`](/docs/components/records/schmitt/#fact-schmitt-electrical-limits) on SN74HC14DR
- [`fact-flipflop-electrical-limits`](/docs/components/records/flipflop/#fact-flipflop-electrical-limits) on SN74HC74DR
- [`fact-npn-pinout`](/docs/components/records/npn/#fact-npn-pinout) on MMBT3904,215

**Conditioned calculations:** none are recorded for this rule.

## precision-feedback-physical-qualification

<EvidenceAnchor id="precision-feedback-physical-qualification" />

**Domain:** precision-output feedback compensation and fault duty

**Verdict:** NEEDS BENCH

**This rule refuses to conclude:** Do not accept populated-output stability, fault current/thermal duty, tolerance, temperature, layout parasitics or factory assembly from exact MPN capture and nominal model sweeps.

**Conditions:** 100 ohm JACK-to-FB resistor and 1 nF DRIVE-to-FB capacitor in the OPA4197 precision-output cell. Manufacturer nominal values and ratings do not prove the assembled feedback loop or protection behavior.

**Records this rule spans:**

- [`rec-precision-feedback-r`](/docs/components/records/precision-feedback-r/) — RC0603FR-07100RL
- [`rec-precision-feedback-c`](/docs/components/records/precision-feedback-c/) — C0603C102J5GACTU

**Facts this rule rests on:** each is published in full on the record page that owns it, at the anchor linked here.

- [`fact-precision-feedback-r-nominal`](/docs/components/records/precision-feedback-r/#fact-precision-feedback-r-nominal) on RC0603FR-07100RL
- [`fact-precision-feedback-r-rating`](/docs/components/records/precision-feedback-r/#fact-precision-feedback-r-rating) on RC0603FR-07100RL
- [`fact-precision-feedback-r-application`](/docs/components/records/precision-feedback-r/#fact-precision-feedback-r-application) on RC0603FR-07100RL
- [`fact-precision-feedback-c-nominal`](/docs/components/records/precision-feedback-c/#fact-precision-feedback-c-nominal) on C0603C102J5GACTU
- [`fact-precision-feedback-c-rating`](/docs/components/records/precision-feedback-c/#fact-precision-feedback-c-rating) on C0603C102J5GACTU
- [`fact-precision-feedback-c-application`](/docs/components/records/precision-feedback-c/#fact-precision-feedback-c-application) on C0603C102J5GACTU

**Conditioned calculations:** none are recorded for this rule.

## Legend

What the recorded terms on this page mean, in ordinary words. The exact terms above are the ones that count; these descriptions explain them and never replace them.

### Rule verdict

| Recorded term | What it means |
| --- | --- |
| NEEDS BENCH | Cannot be settled from documents. It needs measurement on real hardware before it can be relied on. |
| UNSOURCED | No accepted source backs this value yet. Treat it as a claim, not a fact. |

### Domain

| Recorded term | What it means |
| --- | --- |
| precision-output feedback compensation and fault duty | No plain-language description is recorded for this term yet. |
| unselected monitor/reference/latch startup and power loss | No plain-language description is recorded for this term yet. |

## Raw agent resource

These rules are generated from a stored evidence bundle and do not restate it. The bundle is the source of truth: where the two ever disagree, the bundle is right and this page is stale.

- [Open the owning bundle](/docs/claude-skills/circuit-spec-integration/) `circuit-spec-integration`
