Takazudo/zudo-osc-hole-field/doc/src/content/docs/components/records/index.mdx

---
# GENERATED by @takazudo/zudo-circuit-doc — do not edit; run `zudo-circuit-doc generate`
title: "Records"
description: "Per-record evidence pages: facts, sources, coverage domains, pin maps and interactions."
sidebar_position: 3
---

Generated from the component evidence records — edit the records, not this page.

One page per published component record, each carrying that record's facts, sources, coverage domains, pin maps and interactions. They are ordered as the bill of materials orders them, with each subordinate record directly after the part it belongs to.

To compare records against each other, start from the [catalog](/docs/components/catalog/).

## Records

- [PTV09A-4020F-B103](/docs/components/records/b103/) — `rec-b103` panel potentiometer
- [PTV09A-4020F-B104](/docs/components/records/b104/) — `rec-b104` panel potentiometer
- [PTV09A-4020F-B504](/docs/components/records/b504/) — `rec-b504` panel potentiometer
- [SRBV160803](/docs/components/records/srbv/) — `rec-srbv` octave selector
- [WQP518MA](/docs/components/records/wqp518ma/) — `rec-wqp518ma` panel audio jack
- [2MS1T1B1M2QES-5](/docs/components/records/dailywell-2ms1t1b1m2qes-5/) — `rec-dailywell-2ms1t1b1m2qes-5` two-position panel toggle
- [2MS3T1B1M2QES](/docs/components/records/dailywell-2ms3t1b1m2qes/) — `rec-dailywell-2ms3t1b1m2qes` three-position panel toggle
- [B3F-1020](/docs/components/records/omron-b3f-1020/) — `rec-omron-b3f-1020` panel push button
- [APHHS1005QWF/D](/docs/components/records/kingbright-white/) — `rec-kingbright-white` white magnitude and stage indicator emitter
- [APG1005SEC/E-T](/docs/components/records/kingbright-red/) — `rec-kingbright-red` red clip indicator emitter
- [DW254P-2X8-L0](/docs/components/records/dealon-dw254p-2x8-l0/) — `rec-dealon-dw254p-2x8-l0` historical supply-side header candidate; not selected for the current EXT inlet
- [OPA4196IDR](/docs/components/records/op-audio/) — `rec-op-audio` audio; cv; indicator
- [OPA4197IPWR](/docs/components/records/op-precision/) — `rec-op-precision` precision
- [ADG5412FBRUZ](/docs/components/records/fault-switch/) — `rec-fault-switch` jack input fault isolation
- [LM393BIDR](/docs/components/records/comparator/) — `rec-comparator` gate; clip; envelope comparator
- [SN74HC14DR](/docs/components/records/schmitt/) — `rec-schmitt` logic conditioning
- [SN74HC74DR](/docs/components/records/flipflop/) — `rec-flipflop` envelope state
- [SN74HC00DR](/docs/components/records/nand/) — `rec-nand` envelope logic
- [CD74HC221M96](/docs/components/records/one-shot/) — `rec-one-shot` sample pulse
- [LM13700M/NOPB](/docs/components/records/ota/) — `rec-ota` VCA; filter; envelope; folder
- [LF398M/NOPB](/docs/components/records/sample-hold/) — `rec-sample-hold` sample and hold
- [AS3340D](/docs/components/records/vco/) — `rec-vco` oscillator core
- [NOISE2](/docs/components/records/noise/) — `rec-noise` noise source
- [REF5050AIDR](/docs/components/records/reference/) — `rec-reference` 5 V precision reference
- [TLV75533PDBVR](/docs/components/records/regulator-3v3/) — `rec-regulator-3v3` optional local 3.3 V domain
- [BAS16GW-QX](/docs/components/records/signal-diode/) — `rec-signal-diode` rectification; small signal
- [BAT54S,215](/docs/components/records/clamp-diode/) — `rec-clamp-diode` rail clamp pair
- [MMBT3904,215](/docs/components/records/npn/) — `rec-npn` LED current sink; general transistor
- [MMBT3906,215](/docs/components/records/pnp/) — `rec-pnp` general transistor
- [2N7002,215](/docs/components/records/mosfet/) — `rec-mosfet` stage command mute
- [BCM847BS,115](/docs/components/records/matched-npn/) — `rec-matched-npn` matched pair candidate
- [RC0603FR-07100KL](/docs/components/records/r-general/) — `rec-r-general` representative RC0603FR 1% resistor series
- [RT0603BRD07100KL](/docs/components/records/r-precision/) — `rec-r-precision` representative RT0603BRD 0.1% resistor series
- [C0603C101J5GACTU](/docs/components/records/c-small/) — `rec-c-small` 100 pF 50 V C0G compensation series representative
- [C0805C103J5GACTU](/docs/components/records/c-hold/) — `rec-c-hold` 10 nF 50 V C0G hold
- [1206CG104J500NT](/docs/components/records/c-slew/) — `rec-c-slew` proposed slew capacitor; FAMILY specification only; exact MPN applicability UNSOURCED
- [BM03B-GHS-TBT(LF)(SN)](/docs/components/records/gh3-header/) — `rec-gh3-header` board harness header
- [BM07B-GHS-TBT(LF)(SN)](/docs/components/records/gh7-header/) — `rec-gh7-header` board harness header
- [BM08B-GHS-TBT(LF)(SN)](/docs/components/records/gh8-header/) — `rec-gh8-header` board harness header
- [RT0603BRD071KL](/docs/components/records/monitor-rt0603brd071kl/) — `rec-monitor-rt0603brd071kl` unselected monitor resistor
- [RT0603BRD0714KL](/docs/components/records/monitor-rt0603brd0714kl/) — `rec-monitor-rt0603brd0714kl` unselected monitor resistor
- [RT0603BRD075K1L](/docs/components/records/monitor-rt0603brd075k1l/) — `rec-monitor-rt0603brd075k1l` unselected monitor resistor
- [RT0603BRD07150RL](/docs/components/records/monitor-rt0603brd07150rl/) — `rec-monitor-rt0603brd07150rl` unselected monitor resistor
- [RT0603BRD0751KL](/docs/components/records/monitor-rt0603brd0751kl/) — `rec-monitor-rt0603brd0751kl` unselected monitor resistor
- [RT0603BRD074K99L](/docs/components/records/monitor-rt0603brd074k99l/) — `rec-monitor-rt0603brd074k99l` unselected monitor resistor
- [RT0603BRD078K06L](/docs/components/records/monitor-rt0603brd078k06l/) — `rec-monitor-rt0603brd078k06l` unselected monitor resistor
- [RT0603BRD079K09L](/docs/components/records/monitor-rt0603brd079k09l/) — `rec-monitor-rt0603brd079k09l` unselected monitor resistor
- [RC0805FR-0710KL](/docs/components/records/monitor-rc0805fr-0710kl/) — `rec-monitor-rc0805fr-0710kl` unselected monitor resistor
- [RC0805FR-07100KL](/docs/components/records/monitor-rc0805fr-07100kl/) — `rec-monitor-rc0805fr-07100kl` unselected monitor resistor
- [TPS37044MJOFDDFRQ1](/docs/components/records/monitor-tps37044mjofddfrq1/) — `rec-monitor-tps37044mjofddfrq1` unselected quad window supervisor
- [TLV9022DR](/docs/components/records/monitor-tlv9022dr/) — `rec-monitor-tlv9022dr` unselected dual open-drain comparator
- [REF3433TIDBVR](/docs/components/records/monitor-ref3433tidbvr/) — `rec-monitor-ref3433tidbvr` unselected 3.3 V reference without enable
- [SN74LVC1G17DBVR](/docs/components/records/monitor-sn74lvc1g17dbvr/) — `rec-monitor-sn74lvc1g17dbvr` unselected permit Schmitt buffer
- [SN74LVC1G74DCTR](/docs/components/records/monitor-sn74lvc1g74dctr/) — `rec-monitor-sn74lvc1g74dctr` unselected permit D flip-flop
- [C0603C104K5RACTU](/docs/components/records/monitor-c0603c104k5ractu/) — `rec-monitor-c0603c104k5ractu` unselected monitor local bypass capacitor
- [C1206C104F3GACTU](/docs/components/records/monitor-c1206c104f3gactu/) — `rec-monitor-c1206c104f3gactu` unselected reference output C0G bank capacitor
- [RC0603FR-07100RL](/docs/components/records/precision-feedback-r/) — `rec-precision-feedback-r` 100 ohm precision-output feedback resistor
- [C0603C102J5GACTU](/docs/components/records/precision-feedback-c/) — `rec-precision-feedback-c` 1 nF precision-output local compensation capacitor
