Takazudo/zudo-osc-hole-field/doc/src/content/docs/components/records/monitor-c1206c104f3gactu/index.mdx

---
# GENERATED by @takazudo/zudo-circuit-doc — do not edit; run `zudo-circuit-doc generate`
title: "C1206C104F3GACTU"
description: "unselected reference output C0G bank capacitor — KEMET — no placement published — rec-monitor-c1206c104f3gactu"
sidebar_position: 57
---

<EvidenceAnchor id="rec-monitor-c1206c104f3gactu" />

Generated from the component evidence records — edit the records, not this page.

Everything below is projected from this project's stored component evidence. Values keep the exact wording, conditions, units and verdicts they were recorded with — nothing here is re-typed, corrected, or combined into an overall judgement about the part.

This record in the catalog: [C1206C104F3GACTU](/docs/components/catalog/#rec-monitor-c1206c104f3gactu)

## Identity

| Field | Recorded value |
| --- | --- |
| Record ID | `rec-monitor-c1206c104f3gactu` |
| Record kind | standalone |
| Manufacturer part number | `C1206C104F3GACTU` |
| Manufacturer | KEMET |
| Function | unselected reference output C0G bank capacitor |
| LCSC ID | Not assigned; order by exact manufacturer part number |
| Package | `1206 / 3216` |
| Inventory line | `line-monitor-c1206c104f3gactu` |
| Owner skill | `component-monitor-permit-candidates` |

**Fit:** DNP or hand-fit

**Identity state:** VERIFIED

**Source state:** AVAILABLE

**Coverage:** 3 open of 5 published

## Documents and package

<EvidenceAnchor id="component-references-heading" />

<ComponentReferences descriptor="7b2276657273696f6e223a312c22646f63756d656e74223a7b226c6162656c223a2244617461736865657420504446222c227469746c65223a22433132303643313034463347414354552065786163742073706563696669636174696f6e207368656574222c22617574686f72697479223a224d414e5546414354555245525f5052494d415259222c22617661696c6162696c697479223a22415641494c41424c45222c2275726c223a2268747470733a2f2f7777772e796167656f67726f75702e636f6d2f636f6d706f6e656e742d646f63756d656e746174696f6e2f646f776e6c6f61642f7370656373686565742f43313230364331303446334741435455227d2c22666f6f747072696e74223a7b226e616d65223a224b454d45545f43313230365f4330475f44656e7369747942222c22617373657455726c223a222f6173736574732f636f6d706f6e656e742d70726576696577732f666f6f747072696e74732f4b454d45545f43313230365f4330475f44656e73697479422e737667227d2c226d6f64656c44657363726970746f72223a22376232323736363537323733363936663665323233613331326332323730363136333662363136373635343936343232336132323462343534643435353435663433333133323330333635663433333034373566343436353665373336393734373934323232326332323730363136333662363136373635346336313632363536633232336132323462343534643435353435663433333133323330333635663433333034373566343436353665373336393734373934323232326332323664366636343635366335353732366332323361323232663631373337333635373437333266363336663664373036663665363536653734326437303732363537363639363537373733326636643666363436353663373332663462343534643435353435663433333133323330333635663433333034373566343436353665373336393734373934323265373737323663323232633232366636363636373336353734323233613762323237383232336133303263323237393232336133303263323237613232336133303764326332323732366637343631373436393666366532323361376232323738323233613330326332323739323233613330326332323761323233613330376432633232373336333631366336353232336137623232373832323361333132633232373932323361333132633232376132323361333137643764227d" />

**Selected document:** [Datasheet PDF](https://www.yageogroup.com/component-documentation/download/specsheet/C1206C104F3GACTU) — C1206C104F3GACTU exact specification sheet

**Selected source ID:** `src-monitor-c1206c104f3gactu-datasheet`

**Authority:** MANUFACTURER\_PRIMARY

**Availability:** AVAILABLE

**Package footprint:** `KEMET_C1206_C0G_DensityB`

This geometry represents a shared footprint package and may not exactly match the manufacturer part.

## Placements

No board placement is published for this record.

## Coverage

Coverage is stated one domain at a time and is never rolled up. A domain marked open is a question that has not been answered; it is not a finding that the part is unsuitable. A record with no open domains has not thereby been declared safe.

### exact orderable identity

<EvidenceAnchor id="cov-monitor-c1206c104f3gactu-exact-orderable-identity" />

**Coverage ID:** `cov-monitor-c1206c104f3gactu-exact-orderable-identity` · **Status:** COVERED

**Reason:** Exact retained manufacturer identity only; supplier stock remains open.

**Facts in this domain:**

- [`fact-monitor-c1206c104f3gactu-manufacturer`](#fact-monitor-c1206c104f3gactu-manufacturer)
- [`fact-monitor-c1206c104f3gactu-identity`](#fact-monitor-c1206c104f3gactu-identity)

### pinout

<EvidenceAnchor id="cov-monitor-c1206c104f3gactu-pinout" />

**Coverage ID:** `cov-monitor-c1206c104f3gactu-pinout` · **Status:** COVERED

**Reason:** Primary IC pin table or explicit nonpolarized project terminal convention; not an installed-board claim.

**Facts in this domain:**

- [`fact-monitor-c1206c104f3gactu-pinout`](#fact-monitor-c1206c104f3gactu-pinout)

### application qualification

<EvidenceAnchor id="cov-monitor-c1206c104f3gactu-application-qualification" />

**Coverage ID:** `cov-monitor-c1206c104f3gactu-application-qualification` · **Status:** OPEN

**Reason:** UNSOURCED complete startup, bias, timing and power-transition applicability.

**Facts in this domain:**

- [`fact-monitor-c1206c104f3gactu-application-qualification`](#fact-monitor-c1206c104f3gactu-application-qualification)

**Blocked by:** these facts must be resolved before the domain can close. Each is listed in full under Facts.

- [`fact-monitor-c1206c104f3gactu-application-qualification`](#fact-monitor-c1206c104f3gactu-application-qualification)

### mechanical fit

<EvidenceAnchor id="cov-monitor-c1206c104f3gactu-mechanical-fit" />

**Coverage ID:** `cov-monitor-c1206c104f3gactu-mechanical-fit` · **Status:** OPEN

**Reason:** Family CAD needs installed physical and thermal qualification.

**Facts in this domain:**

- [`fact-monitor-c1206c104f3gactu-mechanical-fit`](#fact-monitor-c1206c104f3gactu-mechanical-fit)

**Blocked by:** these facts must be resolved before the domain can close. Each is listed in full under Facts.

- [`fact-monitor-c1206c104f3gactu-mechanical-fit`](#fact-monitor-c1206c104f3gactu-mechanical-fit)

### procurement

<EvidenceAnchor id="cov-monitor-c1206c104f3gactu-procurement" />

**Coverage ID:** `cov-monitor-c1206c104f3gactu-procurement` · **Status:** OPEN

**Reason:** UNSOURCED lifecycle, stock and factory allocation.

**Facts in this domain:**

- [`fact-monitor-c1206c104f3gactu-procurement`](#fact-monitor-c1206c104f3gactu-procurement)

**Blocked by:** these facts must be resolved before the domain can close. Each is listed in full under Facts.

- [`fact-monitor-c1206c104f3gactu-procurement`](#fact-monitor-c1206c104f3gactu-procurement)

## Facts

Each fact keeps its value, its unit, the conditions it holds under, where it came from and how far it has been confirmed as separate fields, because they are separate claims. A value without its conditions is not the same fact, and a verdict is about the evidence for the value, not about the part.

### GUARANTEED\_ELECTRICAL

A parameter the manufacturer guarantees over the stated conditions, usually with minimum, typical and maximum values.

<EvidenceFact>
  <EvidenceAnchor id="fact-monitor-c1206c104f3gactu-capacitance" />

  **Fact:** `fact-monitor-c1206c104f3gactu-capacitance`

  **Value:** 100 · **Unit:** `nF`

  **Conditions:** Nominal capacitance at 1 kHz, 1.0 Vrms; C0G family has zero aging and no applied-DC-voltage change within rating.

  **Verdict:** PASS - primary-source confirmed · **Provenance:** PRIMARY-SPEC

  **Evidence:** [Section/table audit: src-monitor-c1206c104f3gactu-datasheet: physical index0/no printed label, Specifications: Capacitance and Measurement Condition](#src-monitor-c1206c104f3gactu-datasheet)
</EvidenceFact>

<EvidenceFact>
  <EvidenceAnchor id="fact-monitor-c1206c104f3gactu-tolerance" />

  **Fact:** `fact-monitor-c1206c104f3gactu-tolerance`

  **Value:** 0.01 · **Unit:** `fraction`

  **Conditions:** Initial tolerance at the stated capacitance measurement condition; temperature coefficient is applied separately.

  **Verdict:** PASS - primary-source confirmed · **Provenance:** PRIMARY-SPEC

  **Evidence:** [Section/table audit: src-monitor-c1206c104f3gactu-datasheet: physical index0/no printed label, Specifications: Tolerance](#src-monitor-c1206c104f3gactu-datasheet)
</EvidenceFact>

<EvidenceFact>
  <EvidenceAnchor id="fact-monitor-c1206c104f3gactu-rated-voltage" />

  **Fact:** `fact-monitor-c1206c104f3gactu-rated-voltage`

  **Value:** 25 · **Unit:** `V`

  **Conditions:** DC rated voltage; no system fault/overshoot survival qualification.

  **Verdict:** PASS - primary-source confirmed · **Provenance:** PRIMARY-SPEC

  **Evidence:** [Section/table audit: src-monitor-c1206c104f3gactu-datasheet: physical index0/no printed label, Voltage DC](#src-monitor-c1206c104f3gactu-datasheet)
</EvidenceFact>

<EvidenceFact>
  <EvidenceAnchor id="fact-monitor-c1206c104f3gactu-temperature-coefficient" />

  **Fact:** `fact-monitor-c1206c104f3gactu-temperature-coefficient`

  **Value:** 30 · **Unit:** `ppm/°C`

  **Conditions:** Absolute C0G coefficient relative to +25 C and 0 VDC, at 1 kHz/1 Vrms, over -55..125 C; applied-DC behavior is a separate family fact.

  **Verdict:** PASS - primary-source confirmed · **Provenance:** PRIMARY-SPEC

  **Evidence:** [Section/table audit: src-monitor-c1206c104f3gactu-datasheet: physical index0/no printed label, Temperature Range and TCC](#src-monitor-c1206c104f3gactu-datasheet)
</EvidenceFact>

<EvidenceFact>
  <EvidenceAnchor id="fact-monitor-c1206c104f3gactu-temperature-range" />

  **Fact:** `fact-monitor-c1206c104f3gactu-temperature-range`

  **Value:** `maximum`=125; `minimum`=-55 · **Unit:** `°C`

  **Conditions:** Component operating temperature range; actual installed temperature is not established.

  **Verdict:** PASS - primary-source confirmed · **Provenance:** PRIMARY-SPEC

  **Evidence:** [Section/table audit: src-monitor-c1206c104f3gactu-datasheet: physical index0/no printed label, Temperature Range](#src-monitor-c1206c104f3gactu-datasheet)
</EvidenceFact>

<EvidenceFact>
  <EvidenceAnchor id="fact-monitor-c1206c104f3gactu-voltage-change" />

  **Fact:** `fact-monitor-c1206c104f3gactu-voltage-change`

  **Value:** 0 · **Unit:** `fraction`

  **Conditions:** C0G family capacitance does not change with applied rated DC voltage; no bound beyond the exact part voltage rating.

  **Verdict:** PASS - primary-source confirmed · **Provenance:** PRIMARY-SPEC

  **Evidence:** [Section/table audit: src-monitor-c1206c104f3gactu-land: physical index1/printed2, Benefits continued: applied rated DC voltage](#src-monitor-c1206c104f3gactu-land)
</EvidenceFact>

<EvidenceFact>
  <EvidenceAnchor id="fact-monitor-c1206c104f3gactu-aging" />

  **Fact:** `fact-monitor-c1206c104f3gactu-aging`

  **Value:** 0 · **Unit:** `fraction`

  **Conditions:** Zero loss per decade-hour; environmental stress qualification has separate limits.

  **Verdict:** PASS - primary-source confirmed · **Provenance:** PRIMARY-SPEC

  **Evidence:** [Section/table audit: src-monitor-c1206c104f3gactu-datasheet: physical index0/no printed label, Aging Rate](#src-monitor-c1206c104f3gactu-datasheet)
</EvidenceFact>

<EvidenceFact>
  <EvidenceAnchor id="fact-monitor-c1206c104f3gactu-insulation-resistance" />

  **Fact:** `fact-monitor-c1206c104f3gactu-insulation-resistance`

  **Value:** 10000000000 · **Unit:** `ohm`

  **Conditions:** Exact-sheet resistance rating; not a full-temperature or partial-power leakage bound.

  **Verdict:** PASS - primary-source confirmed · **Provenance:** PRIMARY-SPEC

  **Evidence:** [Section/table audit: src-monitor-c1206c104f3gactu-datasheet: physical index0/no printed label, Insulation Resistance](#src-monitor-c1206c104f3gactu-datasheet)
</EvidenceFact>

### PROJECT\_STATE

A value this project recorded about how the part is used here — a chosen operating point, a net assignment, or a derived figure. Not a manufacturer specification.

<EvidenceFact>
  <EvidenceAnchor id="fact-monitor-c1206c104f3gactu-manufacturer" />

  **Fact:** `fact-monitor-c1206c104f3gactu-manufacturer`

  **Value:** KEMET · **Unit:** `NONE`

  **Conditions:** KEMET brand within YAGEO Group; not supplier availability.

  **Verdict:** PASS - primary-source confirmed · **Provenance:** PRIMARY-SPEC

  **Evidence:** [Section/table audit: src-monitor-c1206c104f3gactu-land: physical index0/printed1, Overview](#src-monitor-c1206c104f3gactu-land)
</EvidenceFact>

<EvidenceFact>
  <EvidenceAnchor id="fact-monitor-c1206c104f3gactu-identity" />

  **Fact:** `fact-monitor-c1206c104f3gactu-identity`

  **Value:** `manufacturer`=KEMET; `mpn`=C1206C104F3GACTU; `package`=1206 / 3216 · **Unit:** `NONE`

  **Conditions:** Exact complete order code; no stock or lifecycle inference.

  **Verdict:** PASS - primary-source confirmed · **Provenance:** PRIMARY-SPEC

  **Evidence:** [Section/table audit: src-monitor-c1206c104f3gactu-datasheet: physical index0/no printed label, exact MPN heading and Case Code](#src-monitor-c1206c104f3gactu-datasheet)
</EvidenceFact>

<EvidenceFact>
  <EvidenceAnchor id="fact-monitor-c1206c104f3gactu-pinout" />

  **Fact:** `fact-monitor-c1206c104f3gactu-pinout`

  **Value:** `1`=unpolarized terminal; `2`=unpolarized terminal · **Unit:** `NONE`

  **Conditions:** Project terminal numbers for a nonpolarized capacitor; not manufacturer numbering.

  **Verdict:** NOT APPLICABLE · **Provenance:** PROJECT-CHOICE

  **Evidence:** [Section/table audit: src-monitor-c1206c104f3gactu-candidate: JSON row parts\[id=c1206c104f3gactu\].pins](#src-monitor-c1206c104f3gactu-candidate)
</EvidenceFact>

<EvidenceFact>
  <EvidenceAnchor id="fact-monitor-c1206c104f3gactu-insulation-test-condition" />

  **Fact:** `fact-monitor-c1206c104f3gactu-insulation-test-condition`

  **Value:** Rated voltage applied for 120 +/-5 seconds at 25 C · **Unit:** `NONE`

  **Conditions:** Family IR measurement only; no hot leakage guarantee.

  **Verdict:** PASS - primary-source confirmed · **Provenance:** PRIMARY-SPEC

  **Evidence:** [Section/table audit: src-monitor-c1206c104f3gactu-land: physical index3/printed4, Electrical Parameters: IR limit and footnote3](#src-monitor-c1206c104f3gactu-land)
</EvidenceFact>

<EvidenceFact>
  <EvidenceAnchor id="fact-monitor-c1206c104f3gactu-body-dimensions" />

  **Fact:** `fact-monitor-c1206c104f3gactu-body-dimensions`

  **Value:** `B_mm`=0.5 +/-0.25; `L_mm`=3.2 +/-0.2; `S_mm`=>=1.5; `T_mm`=1.6 +/-0.2; `W_mm`=1.6 +/-0.2 · **Unit:** `NONE`

  **Conditions:** Exact body/termination dimensions, not installed seating or solder fillets.

  **Verdict:** PASS - primary-source confirmed · **Provenance:** PRIMARY-SPEC

  **Evidence:** [Section/table audit: src-monitor-c1206c104f3gactu-datasheet: physical index0/no printed label, Dimensions](#src-monitor-c1206c104f3gactu-datasheet)
</EvidenceFact>

<EvidenceFact>
  <EvidenceAnchor id="fact-monitor-c1206c104f3gactu-land-pattern" />

  **Fact:** `fact-monitor-c1206c104f3gactu-land-pattern`

  **Value:** `C_mm`=1.5; `V1_mm`=4.7; `V2_mm`=2.3; `X_mm`=1.8; `Y_mm`=1.15 · **Unit:** `NONE`

  **Conditions:** Density B reflow lands. C is origin-to-pad centre, Y horizontal length, X vertical height, V1/V2 grid courtyard. Corner shape unspecified.

  **Verdict:** PASS - primary-source confirmed · **Provenance:** PRIMARY-SPEC

  **Evidence:** [Section/table audit: src-monitor-c1206c104f3gactu-land: physical index11/printed12, Table3 1206/3216 DensityB and diagram](#src-monitor-c1206c104f3gactu-land)
</EvidenceFact>

<EvidenceFact>
  <EvidenceAnchor id="fact-monitor-c1206c104f3gactu-application-qualification" />

  **Fact:** `fact-monitor-c1206c104f3gactu-application-qualification`

  **Value:** Capacitance-value range is checked separately. Installed ESR/ESL, leakage, reference startup/precision, power transitions and physical behavior remain unqualified. · **Unit:** `NONE`

  **Conditions:** Unselected isolated monitor candidate, not fitted to the instrument.

  **Verdict:** UNSOURCED · **Provenance:** UNVERIFIED

  **Evidence:** [Section/table audit: src-monitor-c1206c104f3gactu-candidate: JSON row parts\[id=c1206c104f3gactu\]](#src-monitor-c1206c104f3gactu-candidate)
</EvidenceFact>

<EvidenceFact>
  <EvidenceAnchor id="fact-monitor-c1206c104f3gactu-mechanical-fit" />

  **Fact:** `fact-monitor-c1206c104f3gactu-mechanical-fit`

  **Value:** Derived maximum body and recommended lands require installed seating, solderability and clearance qualification. · **Unit:** `NONE`

  **Conditions:** No exact assembly or thermal fit claim.

  **Verdict:** NEEDS BENCH · **Provenance:** PROJECT-CHOICE

  **Evidence:** [Section/table audit: src-monitor-c1206c104f3gactu-candidate: JSON row parts\[id=c1206c104f3gactu\].package\_envelope](#src-monitor-c1206c104f3gactu-candidate)
</EvidenceFact>

<EvidenceFact>
  <EvidenceAnchor id="fact-monitor-c1206c104f3gactu-procurement" />

  **Fact:** `fact-monitor-c1206c104f3gactu-procurement`

  **Value:** Lifecycle, stock, order route and factory allocation remain unverified. · **Unit:** `NONE`

  **Conditions:** A generated specification and shelf-life entry do not establish availability.

  **Verdict:** UNSOURCED · **Provenance:** UNVERIFIED

  **Evidence:** [Section/table audit: src-monitor-c1206c104f3gactu-candidate: JSON row parts\[id=c1206c104f3gactu\]](#src-monitor-c1206c104f3gactu-candidate)
</EvidenceFact>

## Pin maps

The mapping between schematic pins and PCB pads, or physical terminals for an external part, as recorded. A record may carry more than one map when the same part is documented in more than one context.

### pinmap-monitor-c1206c104f3gactu

<EvidenceAnchor id="pinmap-monitor-c1206c104f3gactu" />

- **Symbol:** `C1206C104F3GACTU`
- **Footprint:** `KEMET_C1206_C0G_DensityB`
- **Pins:** 2

<EvidenceDetails label="pin-assignments">
  <EvidenceTable label="pin-assignments">
    | Symbol pin | Name                   | Footprint pad | Function             |
    | ---------- | ---------------------- | ------------- | -------------------- |
    | `1`        | `unpolarized terminal` | `1`           | unpolarized terminal |
    | `2`        | `unpolarized terminal` | `2`           | unpolarized terminal |
  </EvidenceTable>
</EvidenceDetails>

## Interactions

Behaviour that is not a property of this part alone. Each interaction names the records it spans, the conditions it holds under, and how far it has been confirmed. An interaction that spans several parts appears on every one of their pages, under the same identifier, because it is equally a fact about each.

### int-monitor-c1206c104f3gactu

<EvidenceAnchor id="int-monitor-c1206c104f3gactu" />

- **Records involved:** `rec-monitor-c1206c104f3gactu` (this record)
- **Conditions:** Unselected monitor/permit candidate; control supply, reference and fault paths interact.
- **Verdict:** UNSOURCED

**Facts this rests on:**

- [`fact-monitor-c1206c104f3gactu-application-qualification`](#fact-monitor-c1206c104f3gactu-application-qualification)

## Cross-component rules

Rules that span several parts at once and are published in full on the integration page. Each rule's verdict below is that rule's own — it is a statement about the cross-component question, not about this part — and the exact wording of what the rule refuses to conclude is published with the rule itself.

No cross-component rule names this record.

## Sources

Every document cited above, with its identification, when it was retrieved, and what kind of authority it carries. Sources that could not be retrieved are listed too, with their unavailability stated, so a gap in the evidence is visible rather than absent.

### C1206C104F3GACTU exact specification sheet

<EvidenceAnchor id="src-monitor-c1206c104f3gactu-datasheet" />

**Source ID:** `src-monitor-c1206c104f3gactu-datasheet` · **Authority:** MANUFACTURER\_PRIMARY

| Field | Recorded value |
| --- | --- |
| Document number | C1206C104F3GACTU |
| Revision | Generated 10/02/2026; no separate revision printed |
| Document date | 2026-10-02 |
| Retrieved | 2026-10-02 |
| Printed page | not printed |

**Locator:** Exact MPN heading, Dimensions, Specifications and Packaging Specifications tables

**Availability:** AVAILABLE

**Document URL:** [https://www.yageogroup.com/component-documentation/download/specsheet/C1206C104F3GACTU](https://www.yageogroup.com/component-documentation/download/specsheet/C1206C104F3GACTU)

### KEMET Surface Mount Multilayer Ceramic Chip Capacitors C0G Dielectric, 10-250 VDC (Commercial Grade)

<EvidenceAnchor id="src-monitor-c1206c104f3gactu-land" />

**Source ID:** `src-monitor-c1206c104f3gactu-land` · **Authority:** MANUFACTURER\_PRIMARY

| Field | Recorded value |
| --- | --- |
| Document number | C1003\_C0G |
| Revision | 2025-02-20 |
| Document date | 2025-02-20 |
| Retrieved | 2026-10-02 |
| Printed page | 12 |

**Locator:** Table 3, 1206/3216 row, Density Level B and diagram; electrical conditions on printed pages 1, 2 and 4

**Availability:** AVAILABLE

**Document URL:** [https://content.kemet.com/datasheets/KEM\_C1003\_C0G\_SMD.pdf](https://content.kemet.com/datasheets/KEM_C1003_C0G_SMD.pdf)

### Unselected monitor/permit candidate identities

<EvidenceAnchor id="src-monitor-c1206c104f3gactu-candidate" />

**Source ID:** `src-monitor-c1206c104f3gactu-candidate` · **Authority:** PROJECT\_GENERATOR

| Field | Recorded value |
| --- | --- |
| Document number | monitor-permit-parts |
| Revision | source-defined candidate |
| Document date | 2026-10-02 |
| Retrieved | 2026-10-02 |
| Printed page | not paginated |

**Locator:** JSON row parts\[id=c1206c104f3gactu]; status and canonical\_protection\_implemented

**Availability:** AVAILABLE

**Document URL:** no link is published for this source

## Legend

What the recorded terms on this page mean, in ordinary words. The exact terms above are the ones that count; these descriptions explain them and never replace them.

### Verdict

| Recorded term | What it means |
| --- | --- |
| `NEEDS BENCH` | Cannot be settled from documents. It needs measurement on real hardware before it can be relied on. |
| `NOT APPLICABLE` | The parameter does not apply to this part as it is used here. |
| `PASS - primary-source confirmed` | Confirmed against the manufacturer's own document for this exact part. |
| `UNSOURCED` | No accepted source backs this value yet. Treat it as a claim, not a fact. |

### Provenance

| Recorded term | What it means |
| --- | --- |
| `PRIMARY-SPEC` | Taken from the manufacturer's own specification document. |
| `PROJECT-CHOICE` | A decision made by this project. No vendor asserts it. |
| `UNVERIFIED` | Recorded, but not yet backed by an accepted source. |

### Fact class

| Recorded term | What it means |
| --- | --- |
| `GUARANTEED_ELECTRICAL` | A parameter the manufacturer guarantees over the stated conditions, usually with minimum, typical and maximum values. |
| `PROJECT_STATE` | A value this project recorded about how the part is used here — a chosen operating point, a net assignment, or a derived figure. Not a manufacturer specification. |

### Coverage status

| Recorded term | What it means |
| --- | --- |
| `COVERED` | Every question this domain asks is answered by the facts listed against it. |
| `OPEN` | Unresolved. Open means the question has not been answered, not that the part is unsafe — the reason states what is missing. |

### Source availability

| Recorded term | What it means |
| --- | --- |
| `AVAILABLE` | The document was retrieved and is on record. |

### Source authority

| Recorded term | What it means |
| --- | --- |
| `MANUFACTURER_PRIMARY` | The manufacturer's own document for this exact part. |
| `PROJECT_GENERATOR` | A document this project generated, such as a schematic or netlist export. |

### Identity state

| Recorded term | What it means |
| --- | --- |
| `VERIFIED` | The exact orderable part has been confirmed against a source. |

### Source state

| Recorded term | What it means |
| --- | --- |
| `AVAILABLE` | At least one document backing this line was retrieved. |

### Unit

| Recorded term | What it means |
| --- | --- |
| `NONE` | The value is not a physical quantity, so it carries no unit. Recorded as \`NONE\`. |

## Raw agent resource

This page is generated from a stored evidence bundle and does not restate it. The bundle is the source of truth: where the two ever disagree, the bundle is right and this page is stale.

[Open the owning bundle](/docs/claude-skills/component-monitor-permit-candidates/) `component-monitor-permit-candidates`
