Takazudo/zudo-osc-hole-field/doc/src/content/docs/components/records/c-slew/index.mdx

---
# GENERATED by @takazudo/zudo-circuit-doc — do not edit; run `zudo-circuit-doc generate`
title: "1206CG104J500NT"
description: "proposed slew capacitor; FAMILY specification only; exact MPN applicability UNSOURCED — Fenghua Advanced Technology — C46348 — no placement published — rec-c-slew"
sidebar_position: 37
---

<EvidenceAnchor id="rec-c-slew" />

Generated from the component evidence records — edit the records, not this page.

Everything below is projected from this project's stored component evidence. Values keep the exact wording, conditions, units and verdicts they were recorded with — nothing here is re-typed, corrected, or combined into an overall judgement about the part.

This record in the catalog: [1206CG104J500NT](/docs/components/catalog/#rec-c-slew)

## Subordinate record

This is a subordinate record. It is a component in its own right, with its own orderable identity and its own placements, but its evidence is audited as part of [`rec-r-general`](/docs/components/records/r-general/), because its behaviour is only meaningful in that part's circuit. Read the parent record for the shared context; the facts below are the ones specific to this line.

## Identity

| Field | Recorded value |
| --- | --- |
| Record ID | `rec-c-slew` |
| Record kind | subordinate |
| Manufacturer part number | `1206CG104J500NT` |
| Manufacturer | Fenghua Advanced Technology |
| Function | proposed slew capacitor; FAMILY specification only; exact MPN applicability UNSOURCED |
| LCSC ID | `C46348` |
| Package | `1206` |
| Inventory line | `line-c-slew` |
| Also known as | `100 nF 50 V C0G slew bank` |
| Owner skill | `component-passives-family` |

**Fit:** Fitted

**Identity state:** UNRESOLVED

**Source state:** AVAILABLE

**Coverage:** 6 open of 6 published

## Documents and package

<EvidenceAnchor id="component-references-heading" />

<ComponentReferences descriptor="7b2276657273696f6e223a312c22646f63756d656e74223a7b226c6162656c223a2253706563696669636174696f6e20504446222c227469746c65223a224849474820564f4c54414745204d4c434320e2809420486967682d566f6c74616765204d756c74692d6c6179657220436572616d696320436170616369746f72732c2050726f647563742053706563696669636174696f6e222c22617574686f72697479223a224d414e5546414354555245525f4d4952524f52222c22617661696c6162696c697479223a22415641494c41424c45222c2275726c223a2268747470733a2f2f7765622d7374617469632e7061727467656e69652e61692f636f6d706f6e656e742f646f63732f32343831346433343036303432643964356235343833613039366434646634315f323330343134303033305f46482d2d4775616e67646f6e672d46656e676875612d416476616e6365642d546563682d3132303643473130344a3530304e545f4334363334382e706466227d2c22666f6f747072696e74223a7b226e616d65223a224331323036222c22617373657455726c223a222f6173736574732f636f6d706f6e656e742d70726576696577732f666f6f747072696e74732f43313230362e737667227d2c226d6f64656c44657363726970746f72223a22376232323736363537323733363936663665323233613331326332323730363136333662363136373635343936343232336132323433333133323330333632323263323237303631363336623631363736353463363136323635366332323361323234333331333233303336323232633232366436663634363536633535373236633232336132323266363137333733363537343733326636333666366437303666366536353665373432643730373236353736363936353737373332663664366636343635366337333266343333313332333033363566346333333265333232643537333132653336326434383331326533333265373737323663323232633232366636363636373336353734323233613762323237383232336133303263323237393232336133303263323237613232336133303764326332323732366637343631373436393666366532323361376232323738323233613330326332323739323233613330326332323761323233613330376432633232373336333631366336353232336137623232373832323361333132633232373932323361333132633232376132323361333137643764227d" />

**Selected document:** [Specification PDF](https://web-static.partgenie.ai/component/docs/24814d3406042d9d5b5483a096d4df41_2304140030_FH--Guangdong-Fenghua-Advanced-Tech-1206CG104J500NT_C46348.pdf) — HIGH VOLTAGE MLCC — High-Voltage Multi-layer Ceramic Capacitors, Product Specification

**Selected source ID:** `src-c-slew-datasheet`

**Authority:** MANUFACTURER\_MIRROR

**Availability:** AVAILABLE

**Package footprint:** `C1206`

This geometry represents a shared footprint package and may not exactly match the manufacturer part.

## Placements

No board placement is published for this record.

## Coverage

Coverage is stated one domain at a time and is never rolled up. A domain marked open is a question that has not been answered; it is not a finding that the part is unsuitable. A record with no open domains has not thereby been declared safe.

### exact orderable identity

<EvidenceAnchor id="cov-c-slew-exact-orderable-identity" />

**Coverage ID:** `cov-c-slew-exact-orderable-identity` · **Status:** OPEN

**Reason:** The current exact MPN is a project-selected proposal but its full manufacturer orderable identity/package suffix is not confirmed by retained exact-part bytes.

**Facts in this domain:**

- [`fact-c-slew-orderable-identity`](#fact-c-slew-orderable-identity)

**Blocked by:** these facts must be resolved before the domain can close. Each is listed in full under Facts.

- [`fact-c-slew-orderable-identity`](#fact-c-slew-orderable-identity)

### pinout

<EvidenceAnchor id="cov-c-slew-pinout" />

**Coverage ID:** `cov-c-slew-pinout` · **Status:** OPEN

**Reason:** The exact functional pinout is UNSOURCED from retained primary exact-part evidence.

**Facts in this domain:**

- [`fact-c-slew-pinout`](#fact-c-slew-pinout)

**Blocked by:** these facts must be resolved before the domain can close. Each is listed in full under Facts.

- [`fact-c-slew-pinout`](#fact-c-slew-pinout)

### electrical limits

<EvidenceAnchor id="cov-c-slew-electrical-limits" />

**Coverage ID:** `cov-c-slew-electrical-limits` · **Status:** OPEN

**Reason:** No exact-part electrical limits were promoted; source/identity gap remains open.

**Facts in this domain:**

- [`fact-c-slew-electrical-limits`](#fact-c-slew-electrical-limits)

**Blocked by:** these facts must be resolved before the domain can close. Each is listed in full under Facts.

- [`fact-c-slew-electrical-limits`](#fact-c-slew-electrical-limits)

### mechanical fit

<EvidenceAnchor id="cov-c-slew-mechanical-fit" />

**Coverage ID:** `cov-c-slew-mechanical-fit` · **Status:** OPEN

**Reason:** The local family envelope and generic footprint are provisional; physical board fit and land-pattern suitability are not validated.

**Facts in this domain:**

- [`fact-c-slew-mechanical-fit`](#fact-c-slew-mechanical-fit)

**Blocked by:** these facts must be resolved before the domain can close. Each is listed in full under Facts.

- [`fact-c-slew-mechanical-fit`](#fact-c-slew-mechanical-fit)

### procurement

<EvidenceAnchor id="cov-c-slew-procurement" />

**Coverage ID:** `cov-c-slew-procurement` · **Status:** OPEN

**Reason:** Supplier stock, lead time, consignment and assembly allocation remain unverified as of the dated shortlist.

**Facts in this domain:**

- [`fact-c-slew-procurement-status`](#fact-c-slew-procurement-status)

**Blocked by:** these facts must be resolved before the domain can close. Each is listed in full under Facts.

- [`fact-c-slew-procurement-status`](#fact-c-slew-procurement-status)

### exact MPN and value

<EvidenceAnchor id="cov-c-slew-exact-mpn-and-value" />

**Coverage ID:** `cov-c-slew-exact-mpn-and-value` · **Status:** OPEN

**Reason:** The family sheet does not identify the complete exact MPN/value; this remains UNSOURCED.

**Facts in this domain:**

- [`fact-c-slew-exact-value-identity`](#fact-c-slew-exact-value-identity)

**Blocked by:** these facts must be resolved before the domain can close. Each is listed in full under Facts.

- [`fact-c-slew-exact-value-identity`](#fact-c-slew-exact-value-identity)

## Facts

Each fact keeps its value, its unit, the conditions it holds under, where it came from and how far it has been confirmed as separate fields, because they are separate claims. A value without its conditions is not the same fact, and a verdict is about the evidence for the value, not about the part.

### GUARANTEED\_ELECTRICAL

A parameter the manufacturer guarantees over the stated conditions, usually with minimum, typical and maximum values.

<EvidenceFact>
  <EvidenceAnchor id="fact-c-slew-electrical-limits" />

  **Fact:** `fact-c-slew-electrical-limits`

  **Value:** No exact-part electrical limits promoted from retained evidence. · **Unit:** `NONE`

  **Conditions:** The task has not promoted a source-backed limit for this exact shortlist record.

  **Verdict:** UNSOURCED · **Provenance:** UNVERIFIED

  **Evidence:** [src-c-slew-datasheet: exact component electrical-characteristics table not promoted](#src-c-slew-datasheet)
</EvidenceFact>

### PROJECT\_STATE

A value this project recorded about how the part is used here — a chosen operating point, a net assignment, or a derived figure. Not a manufacturer specification.

<EvidenceFact>
  <EvidenceAnchor id="fact-c-slew-manufacturer" />

  **Fact:** `fact-c-slew-manufacturer`

  **Value:** Fenghua Advanced Technology · **Unit:** `NONE`

  **Conditions:** Manufacturer of the project-selected exact shortlist identity.

  **Verdict:** UNSOURCED · **Provenance:** UNVERIFIED

  **Evidence:** [src-c-slew-shortlist: title block or OSC-ES-1 row parts\[id=c\_slew\].manufacturer](#src-c-slew-shortlist)
</EvidenceFact>

<EvidenceFact>
  <EvidenceAnchor id="fact-c-slew-project-selection" />

  **Fact:** `fact-c-slew-project-selection`

  **Value:** `lcsc`=C46348; `manufacturer`=Fenghua Advanced Technology; `mpn`=1206CG104J500NT; `package`=1206; `roles`=100 nF 50 V C0G slew bank; `source_status`=UNVERIFIED · **Unit:** `NONE`

  **Conditions:** OSC-ES-1 dated proposal row; exact source status and availability statements are not supplier allocation.

  **Verdict:** NOT APPLICABLE · **Provenance:** PROJECT-CHOICE

  **Evidence:** [src-c-slew-shortlist: JSON row parts\[id=c\_slew\]](#src-c-slew-shortlist)
</EvidenceFact>

<EvidenceFact>
  <EvidenceAnchor id="fact-c-slew-orderable-identity" />

  **Fact:** `fact-c-slew-orderable-identity`

  **Value:** `manufacturer`=Fenghua Advanced Technology; `mpn`=1206CG104J500NT; `package`=1206 · **Unit:** `NONE`

  **Conditions:** Exact complete orderable identifier in the selected package; does not establish supplier stock.

  **Verdict:** UNSOURCED · **Provenance:** UNVERIFIED

  **Evidence:** [Section/table audit: src-c-slew-datasheet: retained source does not establish complete exact MPN 1206CG104J500NT; see project shortlist selection](#src-c-slew-datasheet)
</EvidenceFact>

<EvidenceFact>
  <EvidenceAnchor id="fact-c-slew-pinout" />

  **Fact:** `fact-c-slew-pinout`

  **Value:** Functional pinout is UNSOURCED; numbers below only retain draft symbol-to-footprint pad positions and do not assign pin functions. · **Unit:** `NONE`

  **Conditions:** No schematic or placement/net binding is claimed. Manufacturer pin functions are source-backed only when a retained primary document names the product family.

  **Verdict:** UNSOURCED · **Provenance:** UNVERIFIED

  **Evidence:** [Section/table audit: src-c-slew-datasheet: source unavailable or exact family-to-MPN link not retained](#src-c-slew-datasheet)
</EvidenceFact>

<EvidenceFact>
  <EvidenceAnchor id="fact-c-slew-procurement-status" />

  **Fact:** `fact-c-slew-procurement-status`

  **Value:** UNVERIFIED · **Unit:** `NONE`

  **Conditions:** Time-stamped OSC-ES-1 state on 2026-09-28; current stock, lead time, consignment, and JLC assembly are not established.

  **Verdict:** UNSOURCED · **Provenance:** PROJECT-CHOICE

  **Evidence:** [src-c-slew-shortlist: JSON row parts\[id=c\_slew\].sourcing.status/jlcpcb\_assembly](#src-c-slew-shortlist)
</EvidenceFact>

<EvidenceFact>
  <EvidenceAnchor id="fact-c-slew-mechanical-fit" />

  **Fact:** `fact-c-slew-mechanical-fit`

  **Value:** Provisional package-family envelope only; board/land-pattern fit has not been physically checked. · **Unit:** `NONE`

  **Conditions:** Selected footprint family and display envelope do not establish exact-part placement or solderability.

  **Verdict:** NEEDS BENCH · **Provenance:** PROJECT-CHOICE

  **Evidence:** [Section/table audit: src-c-slew-shortlist: parts\[id=c\_slew\].package; CAD receipt is provisional family geometry](#src-c-slew-shortlist)
</EvidenceFact>

<EvidenceFact>
  <EvidenceAnchor id="fact-c-slew-exact-value-identity" />

  **Fact:** `fact-c-slew-exact-value-identity`

  **Value:** The retained Fenghua family sheet does not name exact MPN 1206CG104J500NT; value/dielectric/package are not confirmed for this orderable code. · **Unit:** `NONE`

  **Conditions:** The selected Specification PDF is a FAMILY manufacturer mirror, not an exact 1206CG104J500NT datasheet. Exact MPN/value applicability remains UNSOURCED. Source is an available family document hosted by a third party; exact shortlist MPN linkage is not present in its bytes.

  **Verdict:** UNSOURCED · **Provenance:** UNVERIFIED

  **Evidence:** [src-c-slew-risk-ledger: JSON row risks\[id=c\_slew\].reason](#src-c-slew-risk-ledger)
</EvidenceFact>

## Pin maps

The mapping between schematic pins and PCB pads, or physical terminals for an external part, as recorded. A record may carry more than one map when the same part is documented in more than one context.

### pinmap-c-slew

<EvidenceAnchor id="pinmap-c-slew" />

- **Symbol:** `1206CG104J500NT`
- **Footprint:** `C1206`
- **Pins:** 2

<EvidenceDetails label="pin-assignments">
  <EvidenceTable label="pin-assignments">
    | Symbol pin | Name    | Footprint pad | Function                                                                                  |
    | ---------- | ------- | ------------- | ----------------------------------------------------------------------------------------- |
    | `1`        | `Pin 1` | `1`           | Electrical function UNSOURCED; number-to-pad association is retained draft geometry only. |
    | `2`        | `Pin 2` | `2`           | Electrical function UNSOURCED; number-to-pad association is retained draft geometry only. |
  </EvidenceTable>
</EvidenceDetails>

## Interactions

Behaviour that is not a property of this part alone. Each interaction names the records it spans, the conditions it holds under, and how far it has been confirmed. An interaction that spans several parts appears on every one of their pages, under the same identifier, because it is equally a fact about each.

### int-c-slew-project-role

<EvidenceAnchor id="int-c-slew-project-role" />

- **Records involved:** `rec-c-slew` (this record)
- **Conditions:** Project role from OSC-ES-1; schematic nets, board placements, pin assignment and circuit behavior remain unbound.
- **Verdict:** NEEDS BENCH

**Facts this rests on:**

- [`fact-c-slew-project-selection`](#fact-c-slew-project-selection)
- [`fact-c-slew-pinout`](#fact-c-slew-pinout)

## Cross-component rules

Rules that span several parts at once and are published in full on the integration page. Each rule's verdict below is that rule's own — it is a statement about the cross-component question, not about this part — and the exact wording of what the rule refuses to conclude is published with the rule itself.

No cross-component rule names this record.

## Sources

Every document cited above, with its identification, when it was retrieved, and what kind of authority it carries. Sources that could not be retrieved are listed too, with their unavailability stated, so a gap in the evidence is visible rather than absent.

### HIGH VOLTAGE MLCC — High-Voltage Multi-layer Ceramic Capacitors, Product Specification

<EvidenceAnchor id="src-c-slew-datasheet" />

**Source ID:** `src-c-slew-datasheet` · **Authority:** MANUFACTURER\_MIRROR

| Field | Recorded value |
| --- | --- |
| Document number | Document number not identified in retained bytes |
| Revision | A2 |
| Document date | 2025-05-30 |
| Retrieved | 2026-09-28 |
| Printed page | unlabeled |

**Locator:** Visible cover: HIGH VOLTAGE MLCC / High-Voltage Multi-layer Ceramic Capacitors / 0402–2225TYPE; physical index 1 (unlabeled), Revision History, A2 / 2025-5-30 row

**Availability:** AVAILABLE

**Document URL:** [https://web-static.partgenie.ai/component/docs/24814d3406042d9d5b5483a096d4df41\_2304140030\_FH--Guangdong-Fenghua-Advanced-Tech-1206CG104J500NT\_C46348.pdf](https://web-static.partgenie.ai/component/docs/24814d3406042d9d5b5483a096d4df41_2304140030_FH--Guangdong-Fenghua-Advanced-Tech-1206CG104J500NT_C46348.pdf)

### OSC-ES-1 parts shortlist

<EvidenceAnchor id="src-c-slew-shortlist" />

**Source ID:** `src-c-slew-shortlist` · **Authority:** PROJECT\_GENERATOR

| Field | Recorded value |
| --- | --- |
| Document number | OSC-ES-1 |
| Revision | base SHA b185391d30ec38293bc6c5e8b798a282b98baa25 |
| Document date | 2026-09-28 |
| Retrieved | 2026-09-28 |
| Printed page | not paginated |

**Locator:** JSON row parts\[id=c\_slew], fields manufacturer/mpn/package/lcsc/sourcing

**Availability:** AVAILABLE

**Document URL:** [https://github.com/Takazudo/zudo-osc-hole-field/blob/base/osc-hole-field/design/standard/parts-shortlist.json](https://github.com/Takazudo/zudo-osc-hole-field/blob/base/osc-hole-field/design/standard/parts-shortlist.json)

### OSC-ES-1 dated sourcing-risk ledger

<EvidenceAnchor id="src-c-slew-risk-ledger" />

**Source ID:** `src-c-slew-risk-ledger` · **Authority:** PROJECT\_GENERATOR

| Field | Recorded value |
| --- | --- |
| Document number | OSC-ES-1 source/risk appendix |
| Revision | base SHA b185391d30ec38293bc6c5e8b798a282b98baa25 |
| Document date | 2026-09-28 |
| Retrieved | 2026-09-28 |
| Printed page | not paginated |

**Locator:** JSON row risks\[id=c\_slew]

**Availability:** AVAILABLE

**Document URL:** [https://github.com/Takazudo/zudo-osc-hole-field/blob/base/osc-hole-field/design/standard/sourcing-risks.json](https://github.com/Takazudo/zudo-osc-hole-field/blob/base/osc-hole-field/design/standard/sourcing-risks.json)

## Legend

What the recorded terms on this page mean, in ordinary words. The exact terms above are the ones that count; these descriptions explain them and never replace them.

### Verdict

| Recorded term | What it means |
| --- | --- |
| `NEEDS BENCH` | Cannot be settled from documents. It needs measurement on real hardware before it can be relied on. |
| `NOT APPLICABLE` | The parameter does not apply to this part as it is used here. |
| `UNSOURCED` | No accepted source backs this value yet. Treat it as a claim, not a fact. |

### Provenance

| Recorded term | What it means |
| --- | --- |
| `PROJECT-CHOICE` | A decision made by this project. No vendor asserts it. |
| `UNVERIFIED` | Recorded, but not yet backed by an accepted source. |

### Fact class

| Recorded term | What it means |
| --- | --- |
| `GUARANTEED_ELECTRICAL` | A parameter the manufacturer guarantees over the stated conditions, usually with minimum, typical and maximum values. |
| `PROJECT_STATE` | A value this project recorded about how the part is used here — a chosen operating point, a net assignment, or a derived figure. Not a manufacturer specification. |

### Coverage status

| Recorded term | What it means |
| --- | --- |
| `OPEN` | Unresolved. Open means the question has not been answered, not that the part is unsafe — the reason states what is missing. |

### Source availability

| Recorded term | What it means |
| --- | --- |
| `AVAILABLE` | The document was retrieved and is on record. |

### Source authority

| Recorded term | What it means |
| --- | --- |
| `MANUFACTURER_MIRROR` | A copy of a manufacturer document hosted elsewhere. Usable, but weaker than the manufacturer's own copy. |
| `PROJECT_GENERATOR` | A document this project generated, such as a schematic or netlist export. |

### Identity state

| Recorded term | What it means |
| --- | --- |
| `UNRESOLVED`  | The exact orderable part is not yet confirmed. Substituting a same-name part from another vendor is not permitted on that basis. |

### Source state

| Recorded term | What it means |
| --- | --- |
| `AVAILABLE` | At least one document backing this line was retrieved. |

### Unit

| Recorded term | What it means |
| --- | --- |
| `NONE` | The value is not a physical quantity, so it carries no unit. Recorded as \`NONE\`. |

## Raw agent resource

This page is generated from a stored evidence bundle and does not restate it. The bundle is the source of truth: where the two ever disagree, the bundle is right and this page is stale.

[Open the owning bundle](/docs/claude-skills/component-passives-family/) `component-passives-family`
