Takazudo/zudo-osc-hole-field/doc/src/content/docs/components/records/gh8-header/index.mdx

---
# GENERATED by @takazudo/zudo-circuit-doc — do not edit; run `zudo-circuit-doc generate`
title: "BM08B-GHS-TBT(LF)(SN)"
description: "board harness header — JST — no placement published — rec-gh8-header"
sidebar_position: 40
---

<EvidenceAnchor id="rec-gh8-header" />

Generated from the component evidence records — edit the records, not this page.

Everything below is projected from this project's stored component evidence. Values keep the exact wording, conditions, units and verdicts they were recorded with — nothing here is re-typed, corrected, or combined into an overall judgement about the part.

This record in the catalog: [BM08B-GHS-TBT(LF)(SN)](/docs/components/catalog/#rec-gh8-header)

## Identity

| Field | Recorded value |
| --- | --- |
| Record ID | `rec-gh8-header` |
| Record kind | standalone |
| Manufacturer part number | `BM08B-GHS-TBT(LF)(SN)` |
| Manufacturer | JST |
| Function | board harness header |
| LCSC ID | Not assigned; order by exact manufacturer part number |
| Package | `JST_GH8_BM_TopEntry` |
| Inventory line | `line-gh8-header` |
| Owner skill | `component-jst-gh` |

**Fit:** Fitted

**Identity state:** VERIFIED

**Source state:** AVAILABLE

**Coverage:** 1 open of 2 published

## Documents and package

<EvidenceAnchor id="component-references-heading" />

<ComponentReferences descriptor="7b2276657273696f6e223a312c22646f63756d656e74223a7b226c6162656c223a224d656368616e6963616c2064726177696e6720504446222c227469746c65223a224a535420474820436f6e6e6563746f722c20312e3235206d6d2070697463682c204372696d70207374796c6520616e64204d6174696e67207374796c65222c22617574686f72697479223a224d414e5546414354555245525f5052494d415259222c22617661696c6162696c697479223a22415641494c41424c45222c2275726c223a2268747470733a2f2f7777772e6a73742d6d66672e636f6d2f70726f647563742f7064662f656e672f6547482e706466227d2c22666f6f747072696e74223a7b226e616d65223a224a53545f4748385f424d5f546f70456e747279222c22617373657455726c223a222f6173736574732f636f6d706f6e656e742d70726576696577732f666f6f747072696e74732f4a53545f4748385f424d5f546f70456e7472792e737667227d2c226d6f64656c44657363726970746f72223a22376232323736363537323733363936663665323233613331326332323730363136333662363136373635343936343232336132323461353335343566343734383338356634323464356635343666373034353665373437323739323232633232373036313633366236313637363534633631363236353663323233613232346135333534356634373438333835663432346435663534366637303435366537343732373932323263323236643666363436353663353537323663323233613232326636313733373336353734373332663633366636643730366636653635366537343264373037323635373636393635373737333266366436663634363536633733326634613533353435663437343833383566343234643566353436663730343536653734373237393265373737323663323232633232366636363636373336353734323233613762323237383232336133303263323237393232336133303263323237613232336133303764326332323732366637343631373436393666366532323361376232323738323233613330326332323739323233613330326332323761323233613330376432633232373336333631366336353232336137623232373832323361333132633232373932323361333132633232376132323361333137643764227d" />

**Selected document:** [Mechanical drawing PDF](https://www.jst-mfg.com/product/pdf/eng/eGH.pdf) — JST GH Connector, 1.25 mm pitch, Crimp style and Mating style

**Selected source ID:** `src-gh8-header`

**Authority:** MANUFACTURER\_PRIMARY

**Availability:** AVAILABLE

**Package footprint:** `JST_GH8_BM_TopEntry`

This geometry represents a shared footprint package and may not exactly match the manufacturer part.

## Placements

No board placement is published for this record.

## Coverage

Coverage is stated one domain at a time and is never rolled up. A domain marked open is a question that has not been answered; it is not a finding that the part is unsuitable. A record with no open domains has not thereby been declared safe.

### identity

<EvidenceAnchor id="cov-gh8-header-identity" />

**Coverage ID:** `cov-gh8-header-identity` · **Status:** COVERED

**Reason:** Exact manufacturer row retained.

**Facts in this domain:**

- [`fact-gh8-header-identity`](#fact-gh8-header-identity)
- [`fact-gh8-header-rating`](#fact-gh8-header-rating)
- [`fact-gh8-header-geometry`](#fact-gh8-header-geometry)
- [`fact-gh8-header-mate`](#fact-gh8-header-mate)

### mechanical\_fit

<EvidenceAnchor id="cov-gh8-header-mechanical" />

**Coverage ID:** `cov-gh8-header-mechanical` · **Status:** OPEN

**Reason:** Nominal drawing does not qualify installed assembly, derating or loom support.

**Facts in this domain:**

- [`fact-gh8-header-assembly`](#fact-gh8-header-assembly)

**Blocked by:** these facts must be resolved before the domain can close. Each is listed in full under Facts.

- [`fact-gh8-header-assembly`](#fact-gh8-header-assembly)

## Facts

Each fact keeps its value, its unit, the conditions it holds under, where it came from and how far it has been confirmed as separate fields, because they are separate claims. A value without its conditions is not the same fact, and a verdict is about the evidence for the value, not about the part.

### PROJECT\_STATE

A value this project recorded about how the part is used here — a chosen operating point, a net assignment, or a derived figure. Not a manufacturer specification.

<EvidenceFact>
  <EvidenceAnchor id="fact-gh8-header-identity" />

  **Fact:** `fact-gh8-header-identity`

  **Value:** BM08B-GHS-TBT(LF)(SN) · **Unit:** `NONE`

  **Conditions:** Exact JST family table or contact row

  **Verdict:** PASS - primary-source confirmed · **Provenance:** PRIMARY-SPEC

  **Evidence:** [`src-gh8-header`](#src-gh8-header) — eGH printed page 3, exact BM08B-GHS-TBT(LF)(SN) model row; printed page 2 SSHL-002T-P0.2 row for contact
</EvidenceFact>

<EvidenceFact>
  <EvidenceAnchor id="fact-gh8-header-rating" />

  **Fact:** `fact-gh8-header-rating`

  **Value:** 1.0 A AC/DC (AWG 26); 50 V AC/DC; -40 to +105 C including energized temperature rise · **Unit:** `NONE`

  **Conditions:** GH family rating, not an assembled harness derating or all-pin simultaneous guarantee

  **Verdict:** PASS - primary-source confirmed · **Provenance:** PRIMARY-SPEC

  **Evidence:** [`src-gh8-header`](#src-gh8-header) — eGH printed page 1 specifications; page 2 contact row
</EvidenceFact>

<EvidenceFact>
  <EvidenceAnchor id="fact-gh8-header-geometry" />

  **Fact:** `fact-gh8-header-geometry`

  **Value:** Top entry; 1.25 mm pitch; body B=13.25 mm x 4.25 mm, 4.05 mm above PCB; pin 1 at +x mounting view; land 0.6 x 1.7 mm, support 1 x 2.8 mm · **Unit:** `NONE`

  **Conditions:** nominal reference dimensions; no installed tolerance inference

  **Verdict:** PASS - primary-source confirmed · **Provenance:** PRIMARY-SPEC

  **Evidence:** [`src-gh8-header`](#src-gh8-header) — eGH printed page 2 PC board layout top entry Figure and printed page 3 exact model Dimensions (mm) A/B row
</EvidenceFact>

<EvidenceFact>
  <EvidenceAnchor id="fact-gh8-header-assembly" />

  **Fact:** `fact-gh8-header-assembly`

  **Value:** Assembled derating, retention under cable load and bend clearance unqualified · **Unit:** `NONE`

  **Conditions:** physical harness and installed loom require issue #35/57 evidence

  **Verdict:** NEEDS BENCH · **Provenance:** PROJECT-CHOICE

  **Evidence:** [`src-gh8-header`](#src-gh8-header) — eGH printed page 2 Assembly layout reference height 7.3 mm; no bend radius, retention force or assembled derating table on inspected printed pages 1-6
</EvidenceFact>

<EvidenceFact>
  <EvidenceAnchor id="fact-gh8-header-manufacturer" />

  **Fact:** `fact-gh8-header-manufacturer`

  **Value:** JST · **Unit:** `NONE`

  **Conditions:** Manufacturer branding on source PDF

  **Verdict:** PASS - primary-source confirmed · **Provenance:** PRIMARY-SPEC

  **Evidence:** [`src-gh8-header`](#src-gh8-header) — eGH printed page 1 JST footer and printed page 3 header/housing model-number table
</EvidenceFact>

<EvidenceFact>
  <EvidenceAnchor id="fact-gh8-header-mate" />

  **Fact:** `fact-gh8-header-mate`

  **Value:** BM08B-GHS-TBT(LF)(SN) top-entry header mates GHR-08V-S housing with SSHL-002T-P0.2 contact; 7.3 mm mated height is reference only · **Unit:** `NONE`

  **Conditions:** Exact same circuit count; mating face normal to board; no installed loom bend or strain relief inferred

  **Verdict:** PASS - primary-source confirmed · **Provenance:** PRIMARY-SPEC

  **Evidence:** [`src-gh8-header`](#src-gh8-header) — eGH printed page 3 matching Header and Housing model rows; printed page 2 Assembly layout 7.3 reference dimension and Contact row
</EvidenceFact>

## Pin maps

The mapping between schematic pins and PCB pads, or physical terminals for an external part, as recorded. A record may carry more than one map when the same part is documented in more than one context.

### pinmap-gh8-header

<EvidenceAnchor id="pinmap-gh8-header" />

- **Symbol:** `JST_GH8_BM`
- **Footprint:** `JST_GH8_BM_TopEntry`
- **Pins:** 10

<EvidenceDetails label="pin-assignments">
  <EvidenceTable label="pin-assignments">
    | Symbol pin | Name    | Footprint pad | Function           |
    | ---------- | ------- | ------------- | ------------------ |
    | `1`        | `1`     | `1`           | contact\_1         |
    | `2`        | `2`     | `2`           | contact\_2         |
    | `3`        | `3`     | `3`           | contact\_3         |
    | `4`        | `4`     | `4`           | contact\_4         |
    | `5`        | `5`     | `5`           | contact\_5         |
    | `6`        | `6`     | `6`           | contact\_6         |
    | `7`        | `7`     | `7`           | contact\_7         |
    | `8`        | `8`     | `8`           | contact\_8         |
    | `MP1`      | `MOUNT` | `MP1`         | mechanical\_anchor |
    | `MP2`      | `MOUNT` | `MP2`         | mechanical\_anchor |
  </EvidenceTable>
</EvidenceDetails>

## Interactions

Behaviour that is not a property of this part alone. Each interaction names the records it spans, the conditions it holds under, and how far it has been confirmed. An interaction that spans several parts appears on every one of their pages, under the same identifier, because it is equally a fact about each.

### int-gh8-header

<EvidenceAnchor id="int-gh8-header" />

- **Records involved:** `rec-gh8-header` (this record)
- **Conditions:** conditional harness candidate; #35 owns physical location and current allocation
- **Verdict:** NEEDS BENCH

**Facts this rests on:**

- [`fact-gh8-header-geometry`](#fact-gh8-header-geometry)
- [`fact-gh8-header-assembly`](#fact-gh8-header-assembly)

## Cross-component rules

Rules that span several parts at once and are published in full on the integration page. Each rule's verdict below is that rule's own — it is a statement about the cross-component question, not about this part — and the exact wording of what the rule refuses to conclude is published with the rule itself.

No cross-component rule names this record.

## Sources

Every document cited above, with its identification, when it was retrieved, and what kind of authority it carries. Sources that could not be retrieved are listed too, with their unavailability stated, so a gap in the evidence is visible rather than absent.

### JST GH Connector, 1.25 mm pitch, Crimp style and Mating style

<EvidenceAnchor id="src-gh8-header" />

**Source ID:** `src-gh8-header` · **Authority:** MANUFACTURER\_PRIMARY

| Field | Recorded value |
| --- | --- |
| Document number | eGH |
| Revision | not stated in source |
| Document date | not stated in source |
| Retrieved | 2026-09-28 |
| Printed page | 3 |

**Locator:** Page 3 Housing/Header rows, No. 1 circuit drawing; page 2 PC board layout

**Availability:** AVAILABLE

**Document URL:** [https://www.jst-mfg.com/product/pdf/eng/eGH.pdf](https://www.jst-mfg.com/product/pdf/eng/eGH.pdf)

## Legend

What the recorded terms on this page mean, in ordinary words. The exact terms above are the ones that count; these descriptions explain them and never replace them.

### Verdict

| Recorded term | What it means |
| --- | --- |
| `NEEDS BENCH` | Cannot be settled from documents. It needs measurement on real hardware before it can be relied on. |
| `PASS - primary-source confirmed` | Confirmed against the manufacturer's own document for this exact part. |

### Provenance

| Recorded term | What it means |
| --- | --- |
| `PRIMARY-SPEC` | Taken from the manufacturer's own specification document. |
| `PROJECT-CHOICE` | A decision made by this project. No vendor asserts it. |

### Fact class

| Recorded term | What it means |
| --- | --- |
| `PROJECT_STATE` | A value this project recorded about how the part is used here — a chosen operating point, a net assignment, or a derived figure. Not a manufacturer specification. |

### Coverage status

| Recorded term | What it means |
| --- | --- |
| `COVERED` | Every question this domain asks is answered by the facts listed against it. |
| `OPEN` | Unresolved. Open means the question has not been answered, not that the part is unsafe — the reason states what is missing. |

### Source availability

| Recorded term | What it means |
| --- | --- |
| `AVAILABLE` | The document was retrieved and is on record. |

### Source authority

| Recorded term | What it means |
| --- | --- |
| `MANUFACTURER_PRIMARY` | The manufacturer's own document for this exact part. |

### Identity state

| Recorded term | What it means |
| --- | --- |
| `VERIFIED` | The exact orderable part has been confirmed against a source. |

### Source state

| Recorded term | What it means |
| --- | --- |
| `AVAILABLE` | At least one document backing this line was retrieved. |

### Unit

| Recorded term | What it means |
| --- | --- |
| `NONE` | The value is not a physical quantity, so it carries no unit. Recorded as \`NONE\`. |

## Raw agent resource

This page is generated from a stored evidence bundle and does not restate it. The bundle is the source of truth: where the two ever disagree, the bundle is right and this page is stale.

[Open the owning bundle](/docs/claude-skills/component-jst-gh/) `component-jst-gh`
