Takazudo/zudo-osc-hole-field/doc/src/content/docs/components/records/monitor-c0603c104k5ractu/index.mdx

---
# GENERATED by @takazudo/zudo-circuit-doc — do not edit; run `zudo-circuit-doc generate`
title: "C0603C104K5RACTU"
description: "unselected monitor local bypass capacitor — KEMET — no placement published — rec-monitor-c0603c104k5ractu"
sidebar_position: 56
---

<EvidenceAnchor id="rec-monitor-c0603c104k5ractu" />

Generated from the component evidence records — edit the records, not this page.

Everything below is projected from this project's stored component evidence. Values keep the exact wording, conditions, units and verdicts they were recorded with — nothing here is re-typed, corrected, or combined into an overall judgement about the part.

This record in the catalog: [C0603C104K5RACTU](/docs/components/catalog/#rec-monitor-c0603c104k5ractu)

## Identity

| Field | Recorded value |
| --- | --- |
| Record ID | `rec-monitor-c0603c104k5ractu` |
| Record kind | standalone |
| Manufacturer part number | `C0603C104K5RACTU` |
| Manufacturer | KEMET |
| Function | unselected monitor local bypass capacitor |
| LCSC ID | Not assigned; order by exact manufacturer part number |
| Package | `0603 / 1608` |
| Inventory line | `line-monitor-c0603c104k5ractu` |
| Owner skill | `component-monitor-permit-candidates` |

**Fit:** DNP or hand-fit

**Identity state:** VERIFIED

**Source state:** AVAILABLE

**Coverage:** 3 open of 5 published

## Documents and package

<EvidenceAnchor id="component-references-heading" />

<ComponentReferences descriptor="7b2276657273696f6e223a312c22646f63756d656e74223a7b226c6162656c223a2253706563696669636174696f6e20504446222c227469746c65223a224330363033433130344b3552414354552065786163742073706563696669636174696f6e207368656574222c22617574686f72697479223a224d414e5546414354555245525f5052494d415259222c22617661696c6162696c697479223a22415641494c41424c45222c2275726c223a2268747470733a2f2f7777772e796167656f67726f75702e636f6d2f636f6d706f6e656e742d646f63756d656e746174696f6e2f646f776e6c6f61642f7370656373686565742f4330363033433130344b355241435455227d2c22666f6f747072696e74223a7b226e616d65223a224b454d45545f43303630335f44656e7369747942222c22617373657455726c223a222f6173736574732f636f6d706f6e656e742d70726576696577732f666f6f747072696e74732f4b454d45545f43303630335f44656e73697479422e737667227d2c226d6f64656c44657363726970746f72223a22376232323736363537323733363936663665323233613331326332323730363136333662363136373635343936343232336132323462343534643435353435663433333033363330333335663434363536653733363937343739343232323263323237303631363336623631363736353463363136323635366332323361323234623435346434353534356634333330333633303333356634343635366537333639373437393432323232633232366436663634363536633535373236633232336132323266363137333733363537343733326636333666366437303666366536353665373432643730373236353736363936353737373332663664366636343635366337333266346234353464343535343566343333303336333033333566343436353665373336393734373934323265373737323663323232633232366636363636373336353734323233613762323237383232336133303263323237393232336133303263323237613232336133303764326332323732366637343631373436393666366532323361376232323738323233613330326332323739323233613330326332323761323233613330376432633232373336333631366336353232336137623232373832323361333132633232373932323361333132633232376132323361333137643764227d" />

**Selected document:** [Specification PDF](https://www.yageogroup.com/component-documentation/download/specsheet/C0603C104K5RACTU) — C0603C104K5RACTU exact specification sheet

**Selected source ID:** `src-monitor-c0603c104k5ractu-datasheet`

**Authority:** MANUFACTURER\_PRIMARY

**Availability:** AVAILABLE

**Package footprint:** `KEMET_C0603_DensityB`

This geometry represents a shared footprint package and may not exactly match the manufacturer part.

## Placements

No board placement is published for this record.

## Coverage

Coverage is stated one domain at a time and is never rolled up. A domain marked open is a question that has not been answered; it is not a finding that the part is unsuitable. A record with no open domains has not thereby been declared safe.

### exact orderable identity

<EvidenceAnchor id="cov-monitor-c0603c104k5ractu-exact-orderable-identity" />

**Coverage ID:** `cov-monitor-c0603c104k5ractu-exact-orderable-identity` · **Status:** COVERED

**Reason:** Exact retained manufacturer identity only; supplier stock remains open.

**Facts in this domain:**

- [`fact-monitor-c0603c104k5ractu-manufacturer`](#fact-monitor-c0603c104k5ractu-manufacturer)
- [`fact-monitor-c0603c104k5ractu-identity`](#fact-monitor-c0603c104k5ractu-identity)

### pinout

<EvidenceAnchor id="cov-monitor-c0603c104k5ractu-pinout" />

**Coverage ID:** `cov-monitor-c0603c104k5ractu-pinout` · **Status:** COVERED

**Reason:** Primary IC pin table or explicit nonpolarized project terminal convention; not an installed-board claim.

**Facts in this domain:**

- [`fact-monitor-c0603c104k5ractu-pinout`](#fact-monitor-c0603c104k5ractu-pinout)

### application qualification

<EvidenceAnchor id="cov-monitor-c0603c104k5ractu-application-qualification" />

**Coverage ID:** `cov-monitor-c0603c104k5ractu-application-qualification` · **Status:** OPEN

**Reason:** UNSOURCED complete startup, bias, timing and power-transition applicability.

**Facts in this domain:**

- [`fact-monitor-c0603c104k5ractu-application-qualification`](#fact-monitor-c0603c104k5ractu-application-qualification)

**Blocked by:** these facts must be resolved before the domain can close. Each is listed in full under Facts.

- [`fact-monitor-c0603c104k5ractu-application-qualification`](#fact-monitor-c0603c104k5ractu-application-qualification)

### mechanical fit

<EvidenceAnchor id="cov-monitor-c0603c104k5ractu-mechanical-fit" />

**Coverage ID:** `cov-monitor-c0603c104k5ractu-mechanical-fit` · **Status:** OPEN

**Reason:** Family CAD needs installed physical and thermal qualification.

**Facts in this domain:**

- [`fact-monitor-c0603c104k5ractu-mechanical-fit`](#fact-monitor-c0603c104k5ractu-mechanical-fit)

**Blocked by:** these facts must be resolved before the domain can close. Each is listed in full under Facts.

- [`fact-monitor-c0603c104k5ractu-mechanical-fit`](#fact-monitor-c0603c104k5ractu-mechanical-fit)

### procurement

<EvidenceAnchor id="cov-monitor-c0603c104k5ractu-procurement" />

**Coverage ID:** `cov-monitor-c0603c104k5ractu-procurement` · **Status:** OPEN

**Reason:** UNSOURCED lifecycle, stock and factory allocation.

**Facts in this domain:**

- [`fact-monitor-c0603c104k5ractu-procurement`](#fact-monitor-c0603c104k5ractu-procurement)

**Blocked by:** these facts must be resolved before the domain can close. Each is listed in full under Facts.

- [`fact-monitor-c0603c104k5ractu-procurement`](#fact-monitor-c0603c104k5ractu-procurement)

## Facts

Each fact keeps its value, its unit, the conditions it holds under, where it came from and how far it has been confirmed as separate fields, because they are separate claims. A value without its conditions is not the same fact, and a verdict is about the evidence for the value, not about the part.

### GUARANTEED\_ELECTRICAL

A parameter the manufacturer guarantees over the stated conditions, usually with minimum, typical and maximum values.

<EvidenceFact>
  <EvidenceAnchor id="fact-monitor-c0603c104k5ractu-capacitance" />

  **Fact:** `fact-monitor-c0603c104k5ractu-capacitance`

  **Value:** 100 · **Unit:** `nF`

  **Conditions:** Nominal capacitance at 1 kHz, 1.0 Vrms and the exact 48-hour referee time. No DC-biased effective minimum or post-reflow time-zero claim.

  **Verdict:** PASS - primary-source confirmed · **Provenance:** PRIMARY-SPEC

  **Evidence:** [src-monitor-c0603c104k5ractu-datasheet: physical index0/no printed page: Specifications table row: Capacitance and Measurement Condition; exact Aging Rate row selects 48-hour referee time; src-monitor-c0603c104k5ractu-land physical index13/printed14 Capacitance test-condition table applies referee time to measurements including tolerance](#src-monitor-c0603c104k5ractu-datasheet)
</EvidenceFact>

<EvidenceFact>
  <EvidenceAnchor id="fact-monitor-c0603c104k5ractu-tolerance" />

  **Fact:** `fact-monitor-c0603c104k5ractu-tolerance`

  **Value:** 0.1 · **Unit:** `fraction`

  **Conditions:** Tolerance at the stated capacitance measurement condition and 48-hour referee time; not a post-reflow time-zero or combined temperature/bias/aging bound.

  **Verdict:** PASS - primary-source confirmed · **Provenance:** PRIMARY-SPEC

  **Evidence:** [src-monitor-c0603c104k5ractu-datasheet: physical index0/no printed page: Specifications table row: Tolerance; exact Aging Rate row and src-monitor-c0603c104k5ractu-land physical index13/printed14 Capacitance test-condition table](#src-monitor-c0603c104k5ractu-datasheet)
</EvidenceFact>

<EvidenceFact>
  <EvidenceAnchor id="fact-monitor-c0603c104k5ractu-rated-voltage" />

  **Fact:** `fact-monitor-c0603c104k5ractu-rated-voltage`

  **Value:** 50 · **Unit:** `V`

  **Conditions:** DC rated voltage; not a system transient or hot derating qualification.

  **Verdict:** PASS - primary-source confirmed · **Provenance:** PRIMARY-SPEC

  **Evidence:** [src-monitor-c0603c104k5ractu-datasheet: physical index0/no printed page: Specifications table row: Voltage DC](#src-monitor-c0603c104k5ractu-datasheet)
</EvidenceFact>

<EvidenceFact>
  <EvidenceAnchor id="fact-monitor-c0603c104k5ractu-temperature-change" />

  **Fact:** `fact-monitor-c0603c104k5ractu-temperature-change`

  **Value:** 0.15 · **Unit:** `fraction`

  **Conditions:** X7R capacitance variation relative to+25C at0VDC,1kHz1Vrms over-55 to125C. Does not include initial tolerance or DC bias.

  **Verdict:** PASS - primary-source confirmed · **Provenance:** PRIMARY-SPEC

  **Evidence:** [src-monitor-c0603c104k5ractu-datasheet: physical index0/no printed page: Temperature Range and TCC rows](#src-monitor-c0603c104k5ractu-datasheet)
</EvidenceFact>

<EvidenceFact>
  <EvidenceAnchor id="fact-monitor-c0603c104k5ractu-aging" />

  **Fact:** `fact-monitor-c0603c104k5ractu-aging`

  **Value:** 0.03 · **Unit:** `fraction`

  **Conditions:** Stated loss per decade-hour;48-hour referee time. Not a fixed lifetime loss or installed thermal-history result.

  **Verdict:** PASS - primary-source confirmed · **Provenance:** PRIMARY-SPEC

  **Evidence:** [src-monitor-c0603c104k5ractu-datasheet: physical index0/no printed page: Specifications table row: Aging Rate](#src-monitor-c0603c104k5ractu-datasheet)
</EvidenceFact>

<EvidenceFact>
  <EvidenceAnchor id="fact-monitor-c0603c104k5ractu-insulation-resistance" />

  **Fact:** `fact-monitor-c0603c104k5ractu-insulation-resistance`

  **Value:** 5000000000 · **Unit:** `ohm`

  **Conditions:** Exact-sheet rating; no hot/partial-power leakage bound. Family test conditions are a separate fact.

  **Verdict:** PASS - primary-source confirmed · **Provenance:** PRIMARY-SPEC

  **Evidence:** [src-monitor-c0603c104k5ractu-datasheet: physical index0/no printed page: Insulation Resistance section](#src-monitor-c0603c104k5ractu-datasheet)
</EvidenceFact>

### PROJECT\_STATE

A value this project recorded about how the part is used here — a chosen operating point, a net assignment, or a derived figure. Not a manufacturer specification.

<EvidenceFact>
  <EvidenceAnchor id="fact-monitor-c0603c104k5ractu-manufacturer" />

  **Fact:** `fact-monitor-c0603c104k5ractu-manufacturer`

  **Value:** KEMET · **Unit:** `NONE`

  **Conditions:** KEMET brand within YAGEO Group; not supplier availability.

  **Verdict:** PASS - primary-source confirmed · **Provenance:** PRIMARY-SPEC

  **Evidence:** [src-monitor-c0603c104k5ractu-land: physical index0/printed1: Overview section: KEMET X7R description](#src-monitor-c0603c104k5ractu-land)
</EvidenceFact>

<EvidenceFact>
  <EvidenceAnchor id="fact-monitor-c0603c104k5ractu-identity" />

  **Fact:** `fact-monitor-c0603c104k5ractu-identity`

  **Value:** `manufacturer`=KEMET; `mpn`=C0603C104K5RACTU; `package`=0603 / 1608 · **Unit:** `NONE`

  **Conditions:** Complete exact order code; no stock or lifecycle inference.

  **Verdict:** PASS - primary-source confirmed · **Provenance:** PRIMARY-SPEC

  **Evidence:** [src-monitor-c0603c104k5ractu-datasheet: physical index0/no printed page: exact MPN heading and case-code row](#src-monitor-c0603c104k5ractu-datasheet)
</EvidenceFact>

<EvidenceFact>
  <EvidenceAnchor id="fact-monitor-c0603c104k5ractu-pinout" />

  **Fact:** `fact-monitor-c0603c104k5ractu-pinout`

  **Value:** `1`=unpolarized terminal; `2`=unpolarized terminal · **Unit:** `NONE`

  **Conditions:** Project terminal numbers for a nonpolarized two-terminal capacitor; no manufacturer numbering inferred.

  **Verdict:** NOT APPLICABLE · **Provenance:** PROJECT-CHOICE

  **Evidence:** [src-monitor-c0603c104k5ractu-candidate: JSON row parts\[id=c0603c104k5ractu\]; pins1/2 convention](#src-monitor-c0603c104k5ractu-candidate)
</EvidenceFact>

<EvidenceFact>
  <EvidenceAnchor id="fact-monitor-c0603c104k5ractu-insulation-test-condition" />

  **Fact:** `fact-monitor-c0603c104k5ractu-insulation-test-condition`

  **Value:** Rated voltage applied for120s at25C · **Unit:** `NONE`

  **Conditions:** General family measurement condition only; not a hot or partial-power bound.

  **Verdict:** PASS - primary-source confirmed · **Provenance:** PRIMARY-SPEC

  **Evidence:** [src-monitor-c0603c104k5ractu-land: physical index14/printed15: Insulation Resistance section test condition](#src-monitor-c0603c104k5ractu-land)
</EvidenceFact>

<EvidenceFact>
  <EvidenceAnchor id="fact-monitor-c0603c104k5ractu-body-dimensions" />

  **Fact:** `fact-monitor-c0603c104k5ractu-body-dimensions`

  **Value:** `B_mm`=0.35 +/-0.15; `L_mm`=1.6 +/-0.15; `S_mm`=>=0.5; `T_mm`=0.8 +/-0.15; `W_mm`=0.8 +/-0.15 · **Unit:** `NONE`

  **Conditions:** Exact specification dimensions, not installed seating or solder fillets.

  **Verdict:** PASS - primary-source confirmed · **Provenance:** PRIMARY-SPEC

  **Evidence:** [src-monitor-c0603c104k5ractu-datasheet: physical index0/no printed page: Dimensions table](#src-monitor-c0603c104k5ractu-datasheet)
</EvidenceFact>

<EvidenceFact>
  <EvidenceAnchor id="fact-monitor-c0603c104k5ractu-land-pattern" />

  **Fact:** `fact-monitor-c0603c104k5ractu-land-pattern`

  **Value:** `C_mm`=0.8; `V1_mm`=3.1; `V2_mm`=1.5; `X_mm`=1; `Y_mm`=0.95 · **Unit:** `NONE`

  **Conditions:** DensityB recommended reflow geometry. C is origin-to-pad centre; Y horizontal pad length; X vertical pad height; V1/V2 grid-placement courtyard. Pad corner shape unspecified.

  **Verdict:** PASS - primary-source confirmed · **Provenance:** PRIMARY-SPEC

  **Evidence:** [src-monitor-c0603c104k5ractu-land: physical index11/printed12: Table3,0603/1608 row,DensityB and diagram](#src-monitor-c0603c104k5ractu-land)
</EvidenceFact>

<EvidenceFact>
  <EvidenceAnchor id="fact-monitor-c0603c104k5ractu-application-qualification" />

  **Fact:** `fact-monitor-c0603c104k5ractu-application-qualification`

  **Value:** Effective DC-biased capacitance, capacitor leakage, aging/thermal history, REF3433 startup and partial-power behavior remain unestablished. · **Unit:** `NONE`

  **Conditions:** Unselected isolated monitor candidate; not fitted to the instrument.

  **Verdict:** UNSOURCED · **Provenance:** UNVERIFIED

  **Evidence:** [src-monitor-c0603c104k5ractu-candidate: JSON row parts\[id=c0603c104k5ractu\]; unselected candidate status](#src-monitor-c0603c104k5ractu-candidate)
</EvidenceFact>

<EvidenceFact>
  <EvidenceAnchor id="fact-monitor-c0603c104k5ractu-mechanical-fit" />

  **Fact:** `fact-monitor-c0603c104k5ractu-mechanical-fit`

  **Value:** Derived maximum body display and recommended lands require installed solderability, seating and clearance qualification. · **Unit:** `NONE`

  **Conditions:** Unselected isolated monitor candidate; not fitted to the instrument.

  **Verdict:** NEEDS BENCH · **Provenance:** PROJECT-CHOICE

  **Evidence:** [src-monitor-c0603c104k5ractu-candidate: JSON row parts\[id=c0603c104k5ractu\]; unselected candidate status](#src-monitor-c0603c104k5ractu-candidate)
</EvidenceFact>

<EvidenceFact>
  <EvidenceAnchor id="fact-monitor-c0603c104k5ractu-procurement" />

  **Fact:** `fact-monitor-c0603c104k5ractu-procurement`

  **Value:** Manufacturer lifecycle, stock, factory allocation and order route remain unverified. A generated datasheet and78-week shelf-life statement do not establish lifecycle. · **Unit:** `NONE`

  **Conditions:** Unselected isolated monitor candidate; not fitted to the instrument.

  **Verdict:** UNSOURCED · **Provenance:** UNVERIFIED

  **Evidence:** [src-monitor-c0603c104k5ractu-candidate: JSON row parts\[id=c0603c104k5ractu\]; unselected candidate status](#src-monitor-c0603c104k5ractu-candidate)
</EvidenceFact>

## Pin maps

The mapping between schematic pins and PCB pads, or physical terminals for an external part, as recorded. A record may carry more than one map when the same part is documented in more than one context.

### pinmap-monitor-c0603c104k5ractu

<EvidenceAnchor id="pinmap-monitor-c0603c104k5ractu" />

- **Symbol:** `C0603C104K5RACTU`
- **Footprint:** `KEMET_C0603_DensityB`
- **Pins:** 2

<EvidenceDetails label="pin-assignments">
  <EvidenceTable label="pin-assignments">
    | Symbol pin | Name                   | Footprint pad | Function             |
    | ---------- | ---------------------- | ------------- | -------------------- |
    | `1`        | `unpolarized terminal` | `1`           | unpolarized terminal |
    | `2`        | `unpolarized terminal` | `2`           | unpolarized terminal |
  </EvidenceTable>
</EvidenceDetails>

## Interactions

Behaviour that is not a property of this part alone. Each interaction names the records it spans, the conditions it holds under, and how far it has been confirmed. An interaction that spans several parts appears on every one of their pages, under the same identifier, because it is equally a fact about each.

### int-monitor-c0603c104k5ractu

<EvidenceAnchor id="int-monitor-c0603c104k5ractu" />

- **Records involved:** `rec-monitor-c0603c104k5ractu` (this record)
- **Conditions:** Unselected monitor/permit candidate; control supply, reference and fault paths interact.
- **Verdict:** UNSOURCED

**Facts this rests on:**

- [`fact-monitor-c0603c104k5ractu-application-qualification`](#fact-monitor-c0603c104k5ractu-application-qualification)

## Cross-component rules

Rules that span several parts at once and are published in full on the integration page. Each rule's verdict below is that rule's own — it is a statement about the cross-component question, not about this part — and the exact wording of what the rule refuses to conclude is published with the rule itself.

No cross-component rule names this record.

## Sources

Every document cited above, with its identification, when it was retrieved, and what kind of authority it carries. Sources that could not be retrieved are listed too, with their unavailability stated, so a gap in the evidence is visible rather than absent.

### C0603C104K5RACTU exact specification sheet

<EvidenceAnchor id="src-monitor-c0603c104k5ractu-datasheet" />

**Source ID:** `src-monitor-c0603c104k5ractu-datasheet` · **Authority:** MANUFACTURER\_PRIMARY

| Field | Recorded value |
| --- | --- |
| Document number | C0603C104K5RACTU |
| Revision | Generated 10/01/2026; no separate revision printed |
| Document date | 2026-10-01 |
| Retrieved | 2026-10-02 |
| Printed page | not printed |

**Locator:** Exact MPN heading, Dimensions, Specifications and Packaging Specifications tables

**Availability:** AVAILABLE

**Document URL:** [https://www.yageogroup.com/component-documentation/download/specsheet/C0603C104K5RACTU](https://www.yageogroup.com/component-documentation/download/specsheet/C0603C104K5RACTU)

### KEMET Surface Mount Multilayer Ceramic Chip Capacitors X7R Dielectric,6.3-250VDC (Commercial Grade)

<EvidenceAnchor id="src-monitor-c0603c104k5ractu-land" />

**Source ID:** `src-monitor-c0603c104k5ractu-land` · **Authority:** MANUFACTURER\_PRIMARY

| Field | Recorded value |
| --- | --- |
| Document number | C1002\_X7R |
| Revision | 2026-09-01 |
| Document date | 2026-09-01 |
| Retrieved | 2026-10-02 |
| Printed page | 12 |

**Locator:** Table3,0603/1608 row,Density Level B; C/Y/X/V1/V2 labels in diagram

**Availability:** AVAILABLE

**Document URL:** [https://content.kemet.com/datasheets/KEM\_C1002\_X7R\_SMD.pdf](https://content.kemet.com/datasheets/KEM_C1002_X7R_SMD.pdf)

### Unselected monitor/permit candidate identities

<EvidenceAnchor id="src-monitor-c0603c104k5ractu-candidate" />

**Source ID:** `src-monitor-c0603c104k5ractu-candidate` · **Authority:** PROJECT\_GENERATOR

| Field | Recorded value |
| --- | --- |
| Document number | monitor-permit-parts |
| Revision | source-defined candidate |
| Document date | 2026-10-02 |
| Retrieved | 2026-10-02 |
| Printed page | not paginated |

**Locator:** JSON row parts\[id=c0603c104k5ractu]; status and canonical\_protection\_implemented

**Availability:** AVAILABLE

**Document URL:** [https://github.com/Takazudo/zudo-osc-hole-field/blob/main/design/power/monitor-permit-parts.json](https://github.com/Takazudo/zudo-osc-hole-field/blob/main/design/power/monitor-permit-parts.json)

## Legend

What the recorded terms on this page mean, in ordinary words. The exact terms above are the ones that count; these descriptions explain them and never replace them.

### Verdict

| Recorded term | What it means |
| --- | --- |
| `NEEDS BENCH` | Cannot be settled from documents. It needs measurement on real hardware before it can be relied on. |
| `NOT APPLICABLE` | The parameter does not apply to this part as it is used here. |
| `PASS - primary-source confirmed` | Confirmed against the manufacturer's own document for this exact part. |
| `UNSOURCED` | No accepted source backs this value yet. Treat it as a claim, not a fact. |

### Provenance

| Recorded term | What it means |
| --- | --- |
| `PRIMARY-SPEC` | Taken from the manufacturer's own specification document. |
| `PROJECT-CHOICE` | A decision made by this project. No vendor asserts it. |
| `UNVERIFIED` | Recorded, but not yet backed by an accepted source. |

### Fact class

| Recorded term | What it means |
| --- | --- |
| `GUARANTEED_ELECTRICAL` | A parameter the manufacturer guarantees over the stated conditions, usually with minimum, typical and maximum values. |
| `PROJECT_STATE` | A value this project recorded about how the part is used here — a chosen operating point, a net assignment, or a derived figure. Not a manufacturer specification. |

### Coverage status

| Recorded term | What it means |
| --- | --- |
| `COVERED` | Every question this domain asks is answered by the facts listed against it. |
| `OPEN` | Unresolved. Open means the question has not been answered, not that the part is unsafe — the reason states what is missing. |

### Source availability

| Recorded term | What it means |
| --- | --- |
| `AVAILABLE` | The document was retrieved and is on record. |

### Source authority

| Recorded term | What it means |
| --- | --- |
| `MANUFACTURER_PRIMARY` | The manufacturer's own document for this exact part. |
| `PROJECT_GENERATOR` | A document this project generated, such as a schematic or netlist export. |

### Identity state

| Recorded term | What it means |
| --- | --- |
| `VERIFIED` | The exact orderable part has been confirmed against a source. |

### Source state

| Recorded term | What it means |
| --- | --- |
| `AVAILABLE` | At least one document backing this line was retrieved. |

### Unit

| Recorded term | What it means |
| --- | --- |
| `NONE` | The value is not a physical quantity, so it carries no unit. Recorded as \`NONE\`. |

## Raw agent resource

This page is generated from a stored evidence bundle and does not restate it. The bundle is the source of truth: where the two ever disagree, the bundle is right and this page is stale.

[Open the owning bundle](/docs/claude-skills/component-monitor-permit-candidates/) `component-monitor-permit-candidates`
