Takazudo/zudo-osc-hole-field/doc/src/content/docs/components/records/monitor-ref3433tidbvr/index.mdx

---
# GENERATED by @takazudo/zudo-circuit-doc — do not edit; run `zudo-circuit-doc generate`
title: "REF3433TIDBVR"
description: "unselected 3.3 V reference without enable — Texas Instruments — no placement published — rec-monitor-ref3433tidbvr"
sidebar_position: 53
---

<EvidenceAnchor id="rec-monitor-ref3433tidbvr" />

Generated from the component evidence records — edit the records, not this page.

Everything below is projected from this project's stored component evidence. Values keep the exact wording, conditions, units and verdicts they were recorded with — nothing here is re-typed, corrected, or combined into an overall judgement about the part.

This record in the catalog: [REF3433TIDBVR](/docs/components/catalog/#rec-monitor-ref3433tidbvr)

## Identity

| Field | Recorded value |
| --- | --- |
| Record ID | `rec-monitor-ref3433tidbvr` |
| Record kind | standalone |
| Manufacturer part number | `REF3433TIDBVR` |
| Manufacturer | Texas Instruments |
| Function | unselected 3.3 V reference without enable |
| LCSC ID | Not assigned; order by exact manufacturer part number |
| Package | `SOT-23-6 (DBV)` |
| Inventory line | `line-monitor-ref3433tidbvr` |
| Owner skill | `component-monitor-permit-candidates` |

**Fit:** DNP or hand-fit

**Identity state:** VERIFIED

**Source state:** AVAILABLE

**Coverage:** 3 open of 5 published

## Documents and package

<EvidenceAnchor id="component-references-heading" />

<ComponentReferences descriptor="7b2276657273696f6e223a312c22646f63756d656e74223a7b226c6162656c223a2244617461736865657420504446222c227469746c65223a2252454633347878204c6f772d44726966742c204c6f772d506f7765722c20536d616c6c2d466f6f747072696e742053657269657320566f6c74616765205265666572656e6365222c22617574686f72697479223a224d414e5546414354555245525f5052494d415259222c22617661696c6162696c697479223a22415641494c41424c45222c2275726c223a2268747470733a2f2f7777772e74692e636f6d2f6c69742f64732f73796d6c696e6b2f72656633342e706466227d2c22666f6f747072696e74223a7b226e616d65223a22534f542d32332d36222c22617373657455726c223a222f6173736574732f636f6d706f6e656e742d70726576696577732f666f6f747072696e74732f534f542d32332d362e737667227d2c226d6f64656c44657363726970746f72223a22376232323736363537323733363936663665323233613331326332323730363136333662363136373635343936343232336132323533346635343264333233333264333632323263323237303631363336623631363736353463363136323635366332323361323235333466353432643332333332643336323232633232366436663634363536633535373236633232336132323266363137333733363537343733326636333666366437303666366536353665373432643730373236353736363936353737373332663664366636343635366337333266353334663534326433323333326433363265373737323663323232633232366636363636373336353734323233613762323237383232336133303263323237393232336133303263323237613232336133303764326332323732366637343631373436393666366532323361376232323738323233613330326332323739323233613330326332323761323233613330376432633232373336333631366336353232336137623232373832323361333132633232373932323361333132633232376132323361333137643764227d" />

**Selected document:** [Datasheet PDF](https://www.ti.com/lit/ds/symlink/ref34.pdf) — REF34xx Low-Drift, Low-Power, Small-Footprint Series Voltage Reference

**Selected source ID:** `src-monitor-ref3433tidbvr-datasheet`

**Authority:** MANUFACTURER\_PRIMARY

**Availability:** AVAILABLE

**Package footprint:** `SOT-23-6`

This geometry represents a shared footprint package and may not exactly match the manufacturer part.

## Placements

No board placement is published for this record.

## Coverage

Coverage is stated one domain at a time and is never rolled up. A domain marked open is a question that has not been answered; it is not a finding that the part is unsuitable. A record with no open domains has not thereby been declared safe.

### exact orderable identity

<EvidenceAnchor id="cov-monitor-ref3433tidbvr-exact-orderable-identity" />

**Coverage ID:** `cov-monitor-ref3433tidbvr-exact-orderable-identity` · **Status:** COVERED

**Reason:** Exact retained manufacturer identity only; supplier stock remains open.

**Facts in this domain:**

- [`fact-monitor-ref3433tidbvr-manufacturer`](#fact-monitor-ref3433tidbvr-manufacturer)
- [`fact-monitor-ref3433tidbvr-identity`](#fact-monitor-ref3433tidbvr-identity)

### pinout

<EvidenceAnchor id="cov-monitor-ref3433tidbvr-pinout" />

**Coverage ID:** `cov-monitor-ref3433tidbvr-pinout` · **Status:** COVERED

**Reason:** Primary IC pin table or explicit nonpolarized project terminal convention; not an installed-board claim.

**Facts in this domain:**

- [`fact-monitor-ref3433tidbvr-pinout`](#fact-monitor-ref3433tidbvr-pinout)

### application qualification

<EvidenceAnchor id="cov-monitor-ref3433tidbvr-application-qualification" />

**Coverage ID:** `cov-monitor-ref3433tidbvr-application-qualification` · **Status:** OPEN

**Reason:** UNSOURCED complete startup, bias, timing and power-transition applicability.

**Facts in this domain:**

- [`fact-monitor-ref3433tidbvr-application-qualification`](#fact-monitor-ref3433tidbvr-application-qualification)

**Blocked by:** these facts must be resolved before the domain can close. Each is listed in full under Facts.

- [`fact-monitor-ref3433tidbvr-application-qualification`](#fact-monitor-ref3433tidbvr-application-qualification)

### mechanical fit

<EvidenceAnchor id="cov-monitor-ref3433tidbvr-mechanical-fit" />

**Coverage ID:** `cov-monitor-ref3433tidbvr-mechanical-fit` · **Status:** OPEN

**Reason:** Family CAD needs installed physical and thermal qualification.

**Facts in this domain:**

- [`fact-monitor-ref3433tidbvr-mechanical-fit`](#fact-monitor-ref3433tidbvr-mechanical-fit)

**Blocked by:** these facts must be resolved before the domain can close. Each is listed in full under Facts.

- [`fact-monitor-ref3433tidbvr-mechanical-fit`](#fact-monitor-ref3433tidbvr-mechanical-fit)

### procurement

<EvidenceAnchor id="cov-monitor-ref3433tidbvr-procurement" />

**Coverage ID:** `cov-monitor-ref3433tidbvr-procurement` · **Status:** OPEN

**Reason:** UNSOURCED stock and factory allocation.

**Facts in this domain:**

- [`fact-monitor-ref3433tidbvr-procurement`](#fact-monitor-ref3433tidbvr-procurement)

**Blocked by:** these facts must be resolved before the domain can close. Each is listed in full under Facts.

- [`fact-monitor-ref3433tidbvr-procurement`](#fact-monitor-ref3433tidbvr-procurement)

## Facts

Each fact keeps its value, its unit, the conditions it holds under, where it came from and how far it has been confirmed as separate fields, because they are separate claims. A value without its conditions is not the same fact, and a verdict is about the evidence for the value, not about the part.

### RECOMMENDED\_OPERATION

The range the manufacturer intends the part to be used in. Always narrower than the absolute maximum.

<EvidenceFact>
  <EvidenceAnchor id="fact-monitor-ref3433tidbvr-stable-capacitance" />

  **Fact:** `fact-monitor-ref3433tidbvr-stable-capacitance`

  **Value:** `maximum`=0.00001; `minimum`=1e-7 · **Unit:** `F`

  **Conditions:** Effective output capacitance over -40..125C; nominal bypass markings alone do not establish it.

  **Verdict:** PASS - primary-source confirmed · **Provenance:** PRIMARY-SPEC

  **Evidence:** [src-monitor-ref3433tidbvr-datasheet: printed p6 electrical characteristics table, capacitive load](#src-monitor-ref3433tidbvr-datasheet)
</EvidenceFact>

### GUARANTEED\_ELECTRICAL

A parameter the manufacturer guarantees over the stated conditions, usually with minimum, typical and maximum values.

<EvidenceFact>
  <EvidenceAnchor id="fact-monitor-ref3433tidbvr-nominal-output" />

  **Fact:** `fact-monitor-ref3433tidbvr-nominal-output`

  **Value:** 3.3 · **Unit:** `V`

  **Conditions:** Nominal REF3433T option; not a total startup, thermal, aging or loaded-error envelope.

  **Verdict:** PASS - primary-source confirmed · **Provenance:** PRIMARY-SPEC

  **Evidence:** [src-monitor-ref3433tidbvr-datasheet: printed p3 device comparison table](#src-monitor-ref3433tidbvr-datasheet)
</EvidenceFact>

<EvidenceFact>
  <EvidenceAnchor id="fact-monitor-ref3433tidbvr-quiescent-table-max" />

  **Fact:** `fact-monitor-ref3433tidbvr-quiescent-table-max`

  **Value:** 0.000095 · **Unit:** `A`

  **Conditions:** Active mode; VIN=VOUT+VDO, COUT=10uF, CIN=0.1uF, IL=0mA, TA=-40..125C. Output load must additionally be supplied through VIN; actual 5V/0.3uF loaded candidate applicability remains open.

  **Verdict:** PASS - primary-source confirmed · **Provenance:** PRIMARY-SPEC

  **Evidence:** [src-monitor-ref3433tidbvr-datasheet: printed p7 section6.5 IQ row and common table conditions](#src-monitor-ref3433tidbvr-datasheet)
</EvidenceFact>

### TYPICAL\_CURVE

A representative figure read from a characteristic curve. Typical values are not guaranteed and vary part to part.

<EvidenceFact>
  <EvidenceAnchor id="fact-monitor-ref3433tidbvr-startup-nominal" />

  **Fact:** `fact-monitor-ref3433tidbvr-startup-nominal`

  **Value:** 0.0025 · **Unit:** `s`

  **Conditions:** Nominal time to0.1% settling with10uF load; not a maximum.

  **Verdict:** PASS - primary-source confirmed · **Provenance:** PRIMARY-SPEC

  **Evidence:** [src-monitor-ref3433tidbvr-datasheet: printed p6 electrical characteristics table](#src-monitor-ref3433tidbvr-datasheet)
</EvidenceFact>

### TRANSIENT

Behaviour during a short event — startup, a switching edge, a fault or a surge.

<EvidenceFact>
  <EvidenceAnchor id="fact-monitor-ref3433tidbvr-slow-slew" />

  **Fact:** `fact-monitor-ref3433tidbvr-slow-slew`

  **Value:** Slow input transitions can cause output overshoot and shutdown anomalies; source recommends slew near6V/ms. · **Unit:** `NONE`

  **Conditions:** T variant has no enable pin. This does not establish a universal transient envelope.

  **Verdict:** PASS - primary-source confirmed · **Provenance:** PRIMARY-SPEC

  **Evidence:** [src-monitor-ref3433tidbvr-datasheet: printed p19 section9.2.2.3](#src-monitor-ref3433tidbvr-datasheet)
</EvidenceFact>

### PROJECT\_STATE

A value this project recorded about how the part is used here — a chosen operating point, a net assignment, or a derived figure. Not a manufacturer specification.

<EvidenceFact>
  <EvidenceAnchor id="fact-monitor-ref3433tidbvr-manufacturer" />

  **Fact:** `fact-monitor-ref3433tidbvr-manufacturer`

  **Value:** Texas Instruments · **Unit:** `NONE`

  **Conditions:** Exact manufacturer identity; no supplier availability inference.

  **Verdict:** PASS - primary-source confirmed · **Provenance:** PRIMARY-SPEC

  **Evidence:** [src-monitor-ref3433tidbvr-datasheet: manufacturer title block](#src-monitor-ref3433tidbvr-datasheet)
</EvidenceFact>

<EvidenceFact>
  <EvidenceAnchor id="fact-monitor-ref3433tidbvr-identity" />

  **Fact:** `fact-monitor-ref3433tidbvr-identity`

  **Value:** `manufacturer`=Texas Instruments; `mpn`=REF3433TIDBVR; `package`=SOT-23-6 (DBV) · **Unit:** `NONE`

  **Conditions:** Complete exact manufacturer order code; not a stock or factory-allocation statement.

  **Verdict:** PASS - primary-source confirmed · **Provenance:** PRIMARY-SPEC

  **Evidence:** [src-monitor-ref3433tidbvr-datasheet: exact MPN title block or ordering table](#src-monitor-ref3433tidbvr-datasheet)
</EvidenceFact>

<EvidenceFact>
  <EvidenceAnchor id="fact-monitor-ref3433tidbvr-pinout" />

  **Fact:** `fact-monitor-ref3433tidbvr-pinout`

  **Value:** `1`=NC; `2`=GND; `3`=NC; `4`=IN; `5`=NC; `6`=VOUT · **Unit:** `NONE`

  **Conditions:** Manufacturer pin functions only; draft CAD correspondence is separately checked and is not physical qualification.

  **Verdict:** PASS - primary-source confirmed · **Provenance:** PRIMARY-SPEC

  **Evidence:** [src-monitor-ref3433tidbvr-datasheet: Exact variant ordering entries and pin configuration/function table; candidate-specific conditions retained in monitor studies](#src-monitor-ref3433tidbvr-datasheet)
</EvidenceFact>

<EvidenceFact>
  <EvidenceAnchor id="fact-monitor-ref3433tidbvr-application-qualification" />

  **Fact:** `fact-monitor-ref3433tidbvr-application-qualification`

  **Value:** Unselected monitor draft; complete timing, power transitions, leakage, thermal and installed behavior remain unestablished. · **Unit:** `NONE`

  **Conditions:** No electrical protection or manufacturing admission.

  **Verdict:** UNSOURCED · **Provenance:** UNVERIFIED

  **Evidence:** [src-monitor-ref3433tidbvr-candidate: JSON row parts\[id=ref3433tidbvr\]; status and canonical\_protection\_implemented](#src-monitor-ref3433tidbvr-candidate)
</EvidenceFact>

<EvidenceFact>
  <EvidenceAnchor id="fact-monitor-ref3433tidbvr-mechanical-fit" />

  **Fact:** `fact-monitor-ref3433tidbvr-mechanical-fit`

  **Value:** Package-family CAD only; exact installed land pattern, solderability, temperature and clearance need qualification. · **Unit:** `NONE`

  **Conditions:** No board placement is selected for this candidate.

  **Verdict:** NEEDS BENCH · **Provenance:** PROJECT-CHOICE

  **Evidence:** [src-monitor-ref3433tidbvr-candidate: JSON row parts\[id=ref3433tidbvr\]; footprint family](#src-monitor-ref3433tidbvr-candidate)
</EvidenceFact>

<EvidenceFact>
  <EvidenceAnchor id="fact-monitor-ref3433tidbvr-procurement" />

  **Fact:** `fact-monitor-ref3433tidbvr-procurement`

  **Value:** Stock, assembly allocation and order route remain unverified. · **Unit:** `NONE`

  **Conditions:** No purchase, supplier contact or fabrication order.

  **Verdict:** UNSOURCED · **Provenance:** PROJECT-CHOICE

  **Evidence:** [src-monitor-ref3433tidbvr-candidate: JSON row parts\[id=ref3433tidbvr\]; unselected candidate status](#src-monitor-ref3433tidbvr-candidate)
</EvidenceFact>

## Pin maps

The mapping between schematic pins and PCB pads, or physical terminals for an external part, as recorded. A record may carry more than one map when the same part is documented in more than one context.

### pinmap-monitor-ref3433tidbvr

<EvidenceAnchor id="pinmap-monitor-ref3433tidbvr" />

- **Symbol:** `REF3433TIDBVR`
- **Footprint:** `SOT-23-6`
- **Pins:** 6

<EvidenceDetails label="pin-assignments">
  <EvidenceTable label="pin-assignments">
    | Symbol pin | Name   | Footprint pad | Function |
    | ---------- | ------ | ------------- | -------- |
    | `1`        | `NC`   | `1`           | NC       |
    | `2`        | `GND`  | `2`           | GND      |
    | `3`        | `NC`   | `3`           | NC       |
    | `4`        | `IN`   | `4`           | IN       |
    | `5`        | `NC`   | `5`           | NC       |
    | `6`        | `VOUT` | `6`           | VOUT     |
  </EvidenceTable>
</EvidenceDetails>

## Interactions

Behaviour that is not a property of this part alone. Each interaction names the records it spans, the conditions it holds under, and how far it has been confirmed. An interaction that spans several parts appears on every one of their pages, under the same identifier, because it is equally a fact about each.

### int-monitor-ref3433tidbvr

<EvidenceAnchor id="int-monitor-ref3433tidbvr" />

- **Records involved:** `rec-monitor-ref3433tidbvr` (this record)
- **Conditions:** Unselected monitor/permit candidate; control supply, reference and fault paths interact.
- **Verdict:** UNSOURCED

**Facts this rests on:**

- [`fact-monitor-ref3433tidbvr-application-qualification`](#fact-monitor-ref3433tidbvr-application-qualification)

## Cross-component rules

Rules that span several parts at once and are published in full on the integration page. Each rule's verdict below is that rule's own — it is a statement about the cross-component question, not about this part — and the exact wording of what the rule refuses to conclude is published with the rule itself.

- [`monitor-permit-startup`](/docs/components/integration/#monitor-permit-startup) — unselected monitor/reference/latch startup and power loss — **rule verdict:** UNSOURCED

[All cross-component rules](/docs/components/integration/)

## Sources

Every document cited above, with its identification, when it was retrieved, and what kind of authority it carries. Sources that could not be retrieved are listed too, with their unavailability stated, so a gap in the evidence is visible rather than absent.

### REF34xx Low-Drift, Low-Power, Small-Footprint Series Voltage Reference

<EvidenceAnchor id="src-monitor-ref3433tidbvr-datasheet" />

**Source ID:** `src-monitor-ref3433tidbvr-datasheet` · **Authority:** MANUFACTURER\_PRIMARY

| Field | Recorded value |
| --- | --- |
| Document number | SBAS804 |
| Revision | G |
| Document date | April 2026 |
| Retrieved | 2026-10-02 |
| Printed page | 4 |

**Locator:** Exact variant ordering entries and pin configuration/function table; candidate-specific conditions retained in monitor studies

**Availability:** AVAILABLE

**Document URL:** [https://www.ti.com/lit/ds/symlink/ref34.pdf](https://www.ti.com/lit/ds/symlink/ref34.pdf)

### Unselected monitor/permit candidate identities

<EvidenceAnchor id="src-monitor-ref3433tidbvr-candidate" />

**Source ID:** `src-monitor-ref3433tidbvr-candidate` · **Authority:** PROJECT\_GENERATOR

| Field | Recorded value |
| --- | --- |
| Document number | monitor-permit-parts |
| Revision | source-defined candidate |
| Document date | 2026-10-02 |
| Retrieved | 2026-10-02 |
| Printed page | not paginated |

**Locator:** JSON row parts\[id=ref3433tidbvr]; status and canonical\_protection\_implemented

**Availability:** AVAILABLE

**Document URL:** [https://github.com/Takazudo/zudo-osc-hole-field/blob/main/design/power/monitor-permit-parts.json](https://github.com/Takazudo/zudo-osc-hole-field/blob/main/design/power/monitor-permit-parts.json)

## Legend

What the recorded terms on this page mean, in ordinary words. The exact terms above are the ones that count; these descriptions explain them and never replace them.

### Verdict

| Recorded term | What it means |
| --- | --- |
| `NEEDS BENCH` | Cannot be settled from documents. It needs measurement on real hardware before it can be relied on. |
| `PASS - primary-source confirmed` | Confirmed against the manufacturer's own document for this exact part. |
| `UNSOURCED` | No accepted source backs this value yet. Treat it as a claim, not a fact. |

### Provenance

| Recorded term | What it means |
| --- | --- |
| `PRIMARY-SPEC` | Taken from the manufacturer's own specification document. |
| `PROJECT-CHOICE` | A decision made by this project. No vendor asserts it. |
| `UNVERIFIED` | Recorded, but not yet backed by an accepted source. |

### Fact class

| Recorded term | What it means |
| --- | --- |
| `GUARANTEED_ELECTRICAL` | A parameter the manufacturer guarantees over the stated conditions, usually with minimum, typical and maximum values. |
| `PROJECT_STATE` | A value this project recorded about how the part is used here — a chosen operating point, a net assignment, or a derived figure. Not a manufacturer specification. |
| `RECOMMENDED_OPERATION` | The range the manufacturer intends the part to be used in. Always narrower than the absolute maximum. |
| `TRANSIENT` | Behaviour during a short event — startup, a switching edge, a fault or a surge. |
| `TYPICAL_CURVE` | A representative figure read from a characteristic curve. Typical values are not guaranteed and vary part to part. |

### Coverage status

| Recorded term | What it means |
| --- | --- |
| `COVERED` | Every question this domain asks is answered by the facts listed against it. |
| `OPEN` | Unresolved. Open means the question has not been answered, not that the part is unsafe — the reason states what is missing. |

### Source availability

| Recorded term | What it means |
| --- | --- |
| `AVAILABLE` | The document was retrieved and is on record. |

### Source authority

| Recorded term | What it means |
| --- | --- |
| `MANUFACTURER_PRIMARY` | The manufacturer's own document for this exact part. |
| `PROJECT_GENERATOR` | A document this project generated, such as a schematic or netlist export. |

### Identity state

| Recorded term | What it means |
| --- | --- |
| `VERIFIED` | The exact orderable part has been confirmed against a source. |

### Source state

| Recorded term | What it means |
| --- | --- |
| `AVAILABLE` | At least one document backing this line was retrieved. |

### Unit

| Recorded term | What it means |
| --- | --- |
| `NONE` | The value is not a physical quantity, so it carries no unit. Recorded as \`NONE\`. |

## Raw agent resource

This page is generated from a stored evidence bundle and does not restate it. The bundle is the source of truth: where the two ever disagree, the bundle is right and this page is stale.

[Open the owning bundle](/docs/claude-skills/component-monitor-permit-candidates/) `component-monitor-permit-candidates`
