Takazudo/zudo-osc-hole-field/doc/src/content/docs/components/records/monitor-sn74lvc1g74dctr/index.mdx

---
# GENERATED by @takazudo/zudo-circuit-doc — do not edit; run `zudo-circuit-doc generate`
title: "SN74LVC1G74DCTR"
description: "unselected permit D flip-flop — Texas Instruments — no placement published — rec-monitor-sn74lvc1g74dctr"
sidebar_position: 55
---

<EvidenceAnchor id="rec-monitor-sn74lvc1g74dctr" />

Generated from the component evidence records — edit the records, not this page.

Everything below is projected from this project's stored component evidence. Values keep the exact wording, conditions, units and verdicts they were recorded with — nothing here is re-typed, corrected, or combined into an overall judgement about the part.

This record in the catalog: [SN74LVC1G74DCTR](/docs/components/catalog/#rec-monitor-sn74lvc1g74dctr)

## Identity

| Field | Recorded value |
| --- | --- |
| Record ID | `rec-monitor-sn74lvc1g74dctr` |
| Record kind | standalone |
| Manufacturer part number | `SN74LVC1G74DCTR` |
| Manufacturer | Texas Instruments |
| Function | unselected permit D flip-flop |
| LCSC ID | Not assigned; order by exact manufacturer part number |
| Package | `SM8 (DCT)` |
| Inventory line | `line-monitor-sn74lvc1g74dctr` |
| Owner skill | `component-monitor-permit-candidates` |

**Fit:** DNP or hand-fit

**Identity state:** VERIFIED

**Source state:** AVAILABLE

**Coverage:** 3 open of 5 published

## Documents and package

<EvidenceAnchor id="component-references-heading" />

<ComponentReferences descriptor="7b2276657273696f6e223a312c22646f63756d656e74223a7b226c6162656c223a2244617461736865657420504446222c227469746c65223a22534e37344c5643314737342053696e676c6520506f7369746976652d456467652d54726967676572656420442d5479706520466c69702d466c6f70207769746820436c65617220616e6420507265736574222c22617574686f72697479223a224d414e5546414354555245525f5052494d415259222c22617661696c6162696c697479223a22415641494c41424c45222c2275726c223a2268747470733a2f2f7777772e74692e636f6d2f6c69742f64732f73796d6c696e6b2f736e37346c7663316737342e706466227d2c22666f6f747072696e74223a7b226e616d65223a2254495f4443543030303841222c22617373657455726c223a222f6173736574732f636f6d706f6e656e742d70726576696577732f666f6f747072696e74732f54495f44435430303038412e737667227d2c226d6f64656c44657363726970746f72223a22376232323736363537323733363936663665323233613331326332323730363136333662363136373635343936343232336132323534343935663434343335343330333033303338343132323263323237303631363336623631363736353463363136323635366332323361323235343439356634343433353433303330333033383431323232633232366436663634363536633535373236633232336132323266363137333733363537343733326636333666366437303666366536353665373432643730373236353736363936353737373332663664366636343635366337333266343934333566353434393566343434333534333033303330333834313265373737323663323232633232366636363636373336353734323233613762323237383232336133303263323237393232336133303263323237613232336133303764326332323732366637343631373436393666366532323361376232323738323233613330326332323739323233613330326332323761323233613330376432633232373336333631366336353232336137623232373832323361333132633232373932323361333132633232376132323361333137643764227d" />

**Selected document:** [Datasheet PDF](https://www.ti.com/lit/ds/symlink/sn74lvc1g74.pdf) — SN74LVC1G74 Single Positive-Edge-Triggered D-Type Flip-Flop with Clear and Preset

**Selected source ID:** `src-monitor-sn74lvc1g74dctr-datasheet`

**Authority:** MANUFACTURER\_PRIMARY

**Availability:** AVAILABLE

**Package footprint:** `TI_DCT0008A`

This geometry represents a shared footprint package and may not exactly match the manufacturer part.

## Placements

No board placement is published for this record.

## Coverage

Coverage is stated one domain at a time and is never rolled up. A domain marked open is a question that has not been answered; it is not a finding that the part is unsuitable. A record with no open domains has not thereby been declared safe.

### exact orderable identity

<EvidenceAnchor id="cov-monitor-sn74lvc1g74dctr-exact-orderable-identity" />

**Coverage ID:** `cov-monitor-sn74lvc1g74dctr-exact-orderable-identity` · **Status:** COVERED

**Reason:** Exact retained manufacturer identity only; supplier stock remains open.

**Facts in this domain:**

- [`fact-monitor-sn74lvc1g74dctr-manufacturer`](#fact-monitor-sn74lvc1g74dctr-manufacturer)
- [`fact-monitor-sn74lvc1g74dctr-identity`](#fact-monitor-sn74lvc1g74dctr-identity)

### pinout

<EvidenceAnchor id="cov-monitor-sn74lvc1g74dctr-pinout" />

**Coverage ID:** `cov-monitor-sn74lvc1g74dctr-pinout` · **Status:** COVERED

**Reason:** Primary IC pin table or explicit nonpolarized project terminal convention; not an installed-board claim.

**Facts in this domain:**

- [`fact-monitor-sn74lvc1g74dctr-pinout`](#fact-monitor-sn74lvc1g74dctr-pinout)

### application qualification

<EvidenceAnchor id="cov-monitor-sn74lvc1g74dctr-application-qualification" />

**Coverage ID:** `cov-monitor-sn74lvc1g74dctr-application-qualification` · **Status:** OPEN

**Reason:** UNSOURCED complete startup, bias, timing and power-transition applicability.

**Facts in this domain:**

- [`fact-monitor-sn74lvc1g74dctr-application-qualification`](#fact-monitor-sn74lvc1g74dctr-application-qualification)

**Blocked by:** these facts must be resolved before the domain can close. Each is listed in full under Facts.

- [`fact-monitor-sn74lvc1g74dctr-application-qualification`](#fact-monitor-sn74lvc1g74dctr-application-qualification)

### mechanical fit

<EvidenceAnchor id="cov-monitor-sn74lvc1g74dctr-mechanical-fit" />

**Coverage ID:** `cov-monitor-sn74lvc1g74dctr-mechanical-fit` · **Status:** OPEN

**Reason:** Family CAD needs installed physical and thermal qualification.

**Facts in this domain:**

- [`fact-monitor-sn74lvc1g74dctr-mechanical-fit`](#fact-monitor-sn74lvc1g74dctr-mechanical-fit)

**Blocked by:** these facts must be resolved before the domain can close. Each is listed in full under Facts.

- [`fact-monitor-sn74lvc1g74dctr-mechanical-fit`](#fact-monitor-sn74lvc1g74dctr-mechanical-fit)

### procurement

<EvidenceAnchor id="cov-monitor-sn74lvc1g74dctr-procurement" />

**Coverage ID:** `cov-monitor-sn74lvc1g74dctr-procurement` · **Status:** OPEN

**Reason:** UNSOURCED stock and factory allocation.

**Facts in this domain:**

- [`fact-monitor-sn74lvc1g74dctr-procurement`](#fact-monitor-sn74lvc1g74dctr-procurement)

**Blocked by:** these facts must be resolved before the domain can close. Each is listed in full under Facts.

- [`fact-monitor-sn74lvc1g74dctr-procurement`](#fact-monitor-sn74lvc1g74dctr-procurement)

## Facts

Each fact keeps its value, its unit, the conditions it holds under, where it came from and how far it has been confirmed as separate fields, because they are separate claims. A value without its conditions is not the same fact, and a verdict is about the evidence for the value, not about the part.

### ABSOLUTE\_MAXIMUM

A never-exceed limit. Reaching it may damage the part; it is not an operating target and there is no margin implied by it.

<EvidenceFact>
  <EvidenceAnchor id="fact-monitor-sn74lvc1g74dctr-absolute-voltages" />

  **Fact:** `fact-monitor-sn74lvc1g74dctr-absolute-voltages`

  **Value:** `VCC_V`=\[-0.5,6.5]; `input_V`=\[-0.5,6.5]; `output_poweroff_V`=\[-0.5,6.5] · **Unit:** `V`

  **Conditions:** Stress limits only; active output range is -0.5V..VCC+0.5V. Functional logic outside recommended operating conditions is not established.

  **Verdict:** PASS - primary-source confirmed · **Provenance:** PRIMARY-SPEC

  **Evidence:** [src-monitor-sn74lvc1g74dctr-datasheet: printed p5 absolute maximum ratings; VCC and VI/VO rows](#src-monitor-sn74lvc1g74dctr-datasheet)
</EvidenceFact>

### RECOMMENDED\_OPERATION

The range the manufacturer intends the part to be used in. Always narrower than the absolute maximum.

<EvidenceFact>
  <EvidenceAnchor id="fact-monitor-sn74lvc1g74dctr-recommended-supply" />

  **Fact:** `fact-monitor-sn74lvc1g74dctr-recommended-supply`

  **Value:** `maximum_V`=5.5; `minimum_V`=1.65; `temperature_C`=\[-40,125] · **Unit:** `NONE`

  **Conditions:** Exact DBV or DCT package; data retention only at1.5V is not active operation or a startup guarantee.

  **Verdict:** PASS - primary-source confirmed · **Provenance:** PRIMARY-SPEC

  **Evidence:** [src-monitor-sn74lvc1g74dctr-datasheet: printed p6 recommended operating conditions; VCC and TA rows](#src-monitor-sn74lvc1g74dctr-datasheet)
</EvidenceFact>

<EvidenceFact>
  <EvidenceAnchor id="fact-monitor-sn74lvc1g74dctr-input-transition-limit" />

  **Fact:** `fact-monitor-sn74lvc1g74dctr-input-transition-limit`

  **Value:** 5 · **Unit:** `ns/V`

  **Conditions:** AtVCC5V +/-0.5V; standard CMOS inputs need sufficiently fast edges. No Schmitt clock input is inferred.

  **Verdict:** PASS - primary-source confirmed · **Provenance:** PRIMARY-SPEC

  **Evidence:** [src-monitor-sn74lvc1g74dctr-datasheet: printed p6 DeltaT/DeltaV row](#src-monitor-sn74lvc1g74dctr-datasheet)
</EvidenceFact>

### GUARANTEED\_ELECTRICAL

A parameter the manufacturer guarantees over the stated conditions, usually with minimum, typical and maximum values.

<EvidenceFact>
  <EvidenceAnchor id="fact-monitor-sn74lvc1g74dctr-quiescent-table-max" />

  **Fact:** `fact-monitor-sn74lvc1g74dctr-quiescent-table-max`

  **Value:** 0.00001 · **Unit:** `A`

  **Conditions:** VCC1.65..5.5V, VI5.5V orGND, IO0, TA-40..125C. Loaded, slow-input and switching current remain separate.

  **Verdict:** PASS - primary-source confirmed · **Provenance:** PRIMARY-SPEC

  **Evidence:** [src-monitor-sn74lvc1g74dctr-datasheet: printed p7 ICC row](#src-monitor-sn74lvc1g74dctr-datasheet)
</EvidenceFact>

<EvidenceFact>
  <EvidenceAnchor id="fact-monitor-sn74lvc1g74dctr-poweroff-leakage-table-max" />

  **Fact:** `fact-monitor-sn74lvc1g74dctr-poweroff-leakage-table-max`

  **Value:** 0.00001 · **Unit:** `A`

  **Conditions:** Magnitude of +/-10uA atVCC0, VIorVO5.5V, TA-40..125C. No default LOW, intermediate-supply state or voltage-wide leakage bound is inferred.

  **Verdict:** PASS - primary-source confirmed · **Provenance:** PRIMARY-SPEC

  **Evidence:** [src-monitor-sn74lvc1g74dctr-datasheet: printed p7 Ioff row](#src-monitor-sn74lvc1g74dctr-datasheet)
</EvidenceFact>

<EvidenceFact>
  <EvidenceAnchor id="fact-monitor-sn74lvc1g74dctr-input-current-table-max" />

  **Fact:** `fact-monitor-sn74lvc1g74dctr-input-current-table-max`

  **Value:** 0.000005 · **Unit:** `A`

  **Conditions:** Magnitude of +/-5uA atVI5.5V orGND,VCC0..5.5V,TA-40..125C. Other input-voltage conditions are not silently extrapolated.

  **Verdict:** PASS - primary-source confirmed · **Provenance:** PRIMARY-SPEC

  **Evidence:** [src-monitor-sn74lvc1g74dctr-datasheet: printed p7 II row](#src-monitor-sn74lvc1g74dctr-datasheet)
</EvidenceFact>

<EvidenceFact>
  <EvidenceAnchor id="fact-monitor-sn74lvc1g74dctr-delta-current-table-max" />

  **Fact:** `fact-monitor-sn74lvc1g74dctr-delta-current-table-max`

  **Value:** 0.0005 · **Unit:** `A`

  **Conditions:** VCC3..5.5V, one inputVCC-0.6V, other inputsVCCorGND, TA-40..125C. This point does not bound an arbitrary slow input ramp.

  **Verdict:** PASS - primary-source confirmed · **Provenance:** PRIMARY-SPEC

  **Evidence:** [src-monitor-sn74lvc1g74dctr-datasheet: printed p7 DeltaICC row](#src-monitor-sn74lvc1g74dctr-datasheet)
</EvidenceFact>

### TYPICAL\_CURVE

A representative figure read from a characteristic curve. Typical values are not guaranteed and vary part to part.

<EvidenceFact>
  <EvidenceAnchor id="fact-monitor-sn74lvc1g74dctr-input-capacitance-typical" />

  **Fact:** `fact-monitor-sn74lvc1g74dctr-input-capacitance-typical`

  **Value:** 5 · **Unit:** `pF`

  **Conditions:** Typical only atVCC3.3V,TA25C,VI=VCC orGND. Not a maximum at5V or during power loss.

  **Verdict:** PASS - primary-source confirmed · **Provenance:** PRIMARY-SPEC

  **Evidence:** [src-monitor-sn74lvc1g74dctr-datasheet: printed p7 CI typical column row](#src-monitor-sn74lvc1g74dctr-datasheet)
</EvidenceFact>

### TRANSIENT

Behaviour during a short event — startup, a switching edge, a fault or a surge.

<EvidenceFact>
  <EvidenceAnchor id="fact-monitor-sn74lvc1g74dctr-switching-table" />

  **Fact:** `fact-monitor-sn74lvc1g74dctr-switching-table`

  **Value:** `clear_inactive_before_clock_min_s`=1.2e-9; `clear_pulse_min_s`=2e-9; `clear_to_Q_max_s`=6.1e-9; `clock_pulse_min_s`=2e-9; `clock_to_Q_max_s`=6.1e-9; `input_edge_max_s`=2.5e-9; `load_F`=5e-11; `supply_V`=\[4.5,5.5]; `temperature_C`=\[-40,125] · **Unit:** `NONE`

  **Conditions:** Source table and measurement conditions only; DCT package temperature range. Actual edges/load and reset/clock sequencing remain unqualified.

  **Verdict:** PASS - primary-source confirmed · **Provenance:** PRIMARY-SPEC

  **Evidence:** [src-monitor-sn74lvc1g74dctr-datasheet: printed p7 sections6.6/6.7; p9 figure7-1 (5V +/-0.5V)](#src-monitor-sn74lvc1g74dctr-datasheet)
</EvidenceFact>

### PROJECT\_STATE

A value this project recorded about how the part is used here — a chosen operating point, a net assignment, or a derived figure. Not a manufacturer specification.

<EvidenceFact>
  <EvidenceAnchor id="fact-monitor-sn74lvc1g74dctr-manufacturer" />

  **Fact:** `fact-monitor-sn74lvc1g74dctr-manufacturer`

  **Value:** Texas Instruments · **Unit:** `NONE`

  **Conditions:** Exact manufacturer identity; no supplier availability inference.

  **Verdict:** PASS - primary-source confirmed · **Provenance:** PRIMARY-SPEC

  **Evidence:** [src-monitor-sn74lvc1g74dctr-datasheet: manufacturer title block](#src-monitor-sn74lvc1g74dctr-datasheet)
</EvidenceFact>

<EvidenceFact>
  <EvidenceAnchor id="fact-monitor-sn74lvc1g74dctr-identity" />

  **Fact:** `fact-monitor-sn74lvc1g74dctr-identity`

  **Value:** `manufacturer`=Texas Instruments; `mpn`=SN74LVC1G74DCTR; `package`=SM8 (DCT) · **Unit:** `NONE`

  **Conditions:** Complete exact manufacturer order code; not a stock or factory-allocation statement.

  **Verdict:** PASS - primary-source confirmed · **Provenance:** PRIMARY-SPEC

  **Evidence:** [src-monitor-sn74lvc1g74dctr-datasheet: exact MPN title block or ordering table](#src-monitor-sn74lvc1g74dctr-datasheet)
</EvidenceFact>

<EvidenceFact>
  <EvidenceAnchor id="fact-monitor-sn74lvc1g74dctr-pinout" />

  **Fact:** `fact-monitor-sn74lvc1g74dctr-pinout`

  **Value:** `1`=CLK; `2`=D; `3`=Q\_N; `4`=GND; `5`=Q; `6`=CLR\_N; `7`=PRE\_N; `8`=VCC · **Unit:** `NONE`

  **Conditions:** Manufacturer pin functions only; draft CAD correspondence is separately checked and is not physical qualification.

  **Verdict:** PASS - primary-source confirmed · **Provenance:** PRIMARY-SPEC

  **Evidence:** [src-monitor-sn74lvc1g74dctr-datasheet: printed p4 exact package pin table](#src-monitor-sn74lvc1g74dctr-datasheet)
</EvidenceFact>

<EvidenceFact>
  <EvidenceAnchor id="fact-monitor-sn74lvc1g74dctr-application-qualification" />

  **Fact:** `fact-monitor-sn74lvc1g74dctr-application-qualification`

  **Value:** Unselected monitor draft; complete timing, power transitions, leakage, thermal and installed behavior remain unestablished. · **Unit:** `NONE`

  **Conditions:** No electrical protection or manufacturing admission.

  **Verdict:** UNSOURCED · **Provenance:** UNVERIFIED

  **Evidence:** [src-monitor-sn74lvc1g74dctr-candidate: JSON row parts\[id=sn74lvc1g74dctr\]; status and canonical\_protection\_implemented](#src-monitor-sn74lvc1g74dctr-candidate)
</EvidenceFact>

<EvidenceFact>
  <EvidenceAnchor id="fact-monitor-sn74lvc1g74dctr-mechanical-fit" />

  **Fact:** `fact-monitor-sn74lvc1g74dctr-mechanical-fit`

  **Value:** Package-family CAD only; exact installed land pattern, solderability, temperature and clearance need qualification. · **Unit:** `NONE`

  **Conditions:** No board placement is selected for this candidate.

  **Verdict:** NEEDS BENCH · **Provenance:** PROJECT-CHOICE

  **Evidence:** [src-monitor-sn74lvc1g74dctr-candidate: JSON row parts\[id=sn74lvc1g74dctr\]; footprint family](#src-monitor-sn74lvc1g74dctr-candidate)
</EvidenceFact>

<EvidenceFact>
  <EvidenceAnchor id="fact-monitor-sn74lvc1g74dctr-procurement" />

  **Fact:** `fact-monitor-sn74lvc1g74dctr-procurement`

  **Value:** Stock, assembly allocation and order route remain unverified. · **Unit:** `NONE`

  **Conditions:** No purchase, supplier contact or fabrication order.

  **Verdict:** UNSOURCED · **Provenance:** PROJECT-CHOICE

  **Evidence:** [src-monitor-sn74lvc1g74dctr-candidate: JSON row parts\[id=sn74lvc1g74dctr\]; unselected candidate status](#src-monitor-sn74lvc1g74dctr-candidate)
</EvidenceFact>

<EvidenceFact>
  <EvidenceAnchor id="fact-monitor-sn74lvc1g74dctr-package-envelope" />

  **Fact:** `fact-monitor-sn74lvc1g74dctr-package-envelope`

  **Value:** `body_max_xyz_mm`=\[3.1,3.1,1.3]; `drawing`=DCT0008A 4220784/D October2025; physical PDF indexes18-20, printed page labels absent; `pad_corner_radius_mm`=0.05; `pad_pitch_mm`=0.65; `pad_row_centres_x_mm`=\[-1.9,1.9]; `pad_size_xy_mm`=\[1.1,0.4] · **Unit:** `NONE`

  **Conditions:** Retained manufacturer example; land pattern and provisional envelope require installed qualification. Body dimensions exclude mold/interlead flash per drawing notes3/4.

  **Verdict:** PASS - primary-source confirmed · **Provenance:** PRIMARY-SPEC

  **Evidence:** [src-monitor-sn74lvc1g74dctr-datasheet: physical PDF indexes18-20, printed page labels absent; package-outline and example land-pattern figures, DCT0008A 4220784/D October2025](#src-monitor-sn74lvc1g74dctr-datasheet)
</EvidenceFact>

## Pin maps

The mapping between schematic pins and PCB pads, or physical terminals for an external part, as recorded. A record may carry more than one map when the same part is documented in more than one context.

### pinmap-monitor-sn74lvc1g74dctr

<EvidenceAnchor id="pinmap-monitor-sn74lvc1g74dctr" />

- **Symbol:** `SN74LVC1G74DCTR`
- **Footprint:** `TI_DCT0008A`
- **Pins:** 8

<EvidenceDetails label="pin-assignments">
  <EvidenceTable label="pin-assignments">
    | Symbol pin | Name    | Footprint pad | Function |
    | ---------- | ------- | ------------- | -------- |
    | `1`        | `CLK`   | `1`           | CLK      |
    | `2`        | `D`     | `2`           | D        |
    | `3`        | `Q_N`   | `3`           | Q\_N     |
    | `4`        | `GND`   | `4`           | GND      |
    | `5`        | `Q`     | `5`           | Q        |
    | `6`        | `CLR_N` | `6`           | CLR\_N   |
    | `7`        | `PRE_N` | `7`           | PRE\_N   |
    | `8`        | `VCC`   | `8`           | VCC      |
  </EvidenceTable>
</EvidenceDetails>

## Interactions

Behaviour that is not a property of this part alone. Each interaction names the records it spans, the conditions it holds under, and how far it has been confirmed. An interaction that spans several parts appears on every one of their pages, under the same identifier, because it is equally a fact about each.

### int-monitor-sn74lvc1g74dctr

<EvidenceAnchor id="int-monitor-sn74lvc1g74dctr" />

- **Records involved:** `rec-monitor-sn74lvc1g74dctr` (this record)
- **Conditions:** Unselected monitor/permit candidate; control supply, reference and fault paths interact.
- **Verdict:** UNSOURCED

**Facts this rests on:**

- [`fact-monitor-sn74lvc1g74dctr-application-qualification`](#fact-monitor-sn74lvc1g74dctr-application-qualification)

## Cross-component rules

Rules that span several parts at once and are published in full on the integration page. Each rule's verdict below is that rule's own — it is a statement about the cross-component question, not about this part — and the exact wording of what the rule refuses to conclude is published with the rule itself.

No cross-component rule names this record.

## Sources

Every document cited above, with its identification, when it was retrieved, and what kind of authority it carries. Sources that could not be retrieved are listed too, with their unavailability stated, so a gap in the evidence is visible rather than absent.

### SN74LVC1G74 Single Positive-Edge-Triggered D-Type Flip-Flop with Clear and Preset

<EvidenceAnchor id="src-monitor-sn74lvc1g74dctr-datasheet" />

**Source ID:** `src-monitor-sn74lvc1g74dctr-datasheet` · **Authority:** MANUFACTURER\_PRIMARY

| Field | Recorded value |
| --- | --- |
| Document number | SCES794 |
| Revision | G |
| Document date | September 2021 |
| Retrieved | 2026-10-02 |
| Printed page | 4 |

**Locator:** Exact package pin table; ordering addendum at physical index14; electrical/timing conditions retained in owner facts

**Availability:** AVAILABLE

**Document URL:** [https://www.ti.com/lit/ds/symlink/sn74lvc1g74.pdf](https://www.ti.com/lit/ds/symlink/sn74lvc1g74.pdf)

### Unselected monitor/permit candidate identities

<EvidenceAnchor id="src-monitor-sn74lvc1g74dctr-candidate" />

**Source ID:** `src-monitor-sn74lvc1g74dctr-candidate` · **Authority:** PROJECT\_GENERATOR

| Field | Recorded value |
| --- | --- |
| Document number | monitor-permit-parts |
| Revision | source-defined candidate |
| Document date | 2026-10-02 |
| Retrieved | 2026-10-02 |
| Printed page | not paginated |

**Locator:** JSON row parts\[id=sn74lvc1g74dctr]; status and canonical\_protection\_implemented

**Availability:** AVAILABLE

**Document URL:** [https://github.com/Takazudo/zudo-osc-hole-field/blob/main/design/power/monitor-permit-parts.json](https://github.com/Takazudo/zudo-osc-hole-field/blob/main/design/power/monitor-permit-parts.json)

## Legend

What the recorded terms on this page mean, in ordinary words. The exact terms above are the ones that count; these descriptions explain them and never replace them.

### Verdict

| Recorded term | What it means |
| --- | --- |
| `NEEDS BENCH` | Cannot be settled from documents. It needs measurement on real hardware before it can be relied on. |
| `PASS - primary-source confirmed` | Confirmed against the manufacturer's own document for this exact part. |
| `UNSOURCED` | No accepted source backs this value yet. Treat it as a claim, not a fact. |

### Provenance

| Recorded term | What it means |
| --- | --- |
| `PRIMARY-SPEC` | Taken from the manufacturer's own specification document. |
| `PROJECT-CHOICE` | A decision made by this project. No vendor asserts it. |
| `UNVERIFIED` | Recorded, but not yet backed by an accepted source. |

### Fact class

| Recorded term | What it means |
| --- | --- |
| `ABSOLUTE_MAXIMUM` | A never-exceed limit. Reaching it may damage the part; it is not an operating target and there is no margin implied by it. |
| `GUARANTEED_ELECTRICAL` | A parameter the manufacturer guarantees over the stated conditions, usually with minimum, typical and maximum values. |
| `PROJECT_STATE` | A value this project recorded about how the part is used here — a chosen operating point, a net assignment, or a derived figure. Not a manufacturer specification. |
| `RECOMMENDED_OPERATION` | The range the manufacturer intends the part to be used in. Always narrower than the absolute maximum. |
| `TRANSIENT` | Behaviour during a short event — startup, a switching edge, a fault or a surge. |
| `TYPICAL_CURVE` | A representative figure read from a characteristic curve. Typical values are not guaranteed and vary part to part. |

### Coverage status

| Recorded term | What it means |
| --- | --- |
| `COVERED` | Every question this domain asks is answered by the facts listed against it. |
| `OPEN` | Unresolved. Open means the question has not been answered, not that the part is unsafe — the reason states what is missing. |

### Source availability

| Recorded term | What it means |
| --- | --- |
| `AVAILABLE` | The document was retrieved and is on record. |

### Source authority

| Recorded term | What it means |
| --- | --- |
| `MANUFACTURER_PRIMARY` | The manufacturer's own document for this exact part. |
| `PROJECT_GENERATOR` | A document this project generated, such as a schematic or netlist export. |

### Identity state

| Recorded term | What it means |
| --- | --- |
| `VERIFIED` | The exact orderable part has been confirmed against a source. |

### Source state

| Recorded term | What it means |
| --- | --- |
| `AVAILABLE` | At least one document backing this line was retrieved. |

### Unit

| Recorded term | What it means |
| --- | --- |
| `NONE` | The value is not a physical quantity, so it carries no unit. Recorded as \`NONE\`. |

## Raw agent resource

This page is generated from a stored evidence bundle and does not restate it. The bundle is the source of truth: where the two ever disagree, the bundle is right and this page is stale.

[Open the owning bundle](/docs/claude-skills/component-monitor-permit-candidates/) `component-monitor-permit-candidates`
