Takazudo/zudo-osc-hole-field/doc/src/content/docs/components/records/dealon-dw254p-2x8-l0/index.mdx

---
# GENERATED by @takazudo/zudo-circuit-doc — do not edit; run `zudo-circuit-doc generate`
title: "DW254P-2X8-L0"
description: "historical supply-side header candidate; not selected for the current EXT inlet — DEALON — C4749189 — no placement published — rec-dealon-dw254p-2x8-l0"
sidebar_position: 12
---

<EvidenceAnchor id="rec-dealon-dw254p-2x8-l0" />

Generated from the component evidence records — edit the records, not this page.

Everything below is projected from this project's stored component evidence. Values keep the exact wording, conditions, units and verdicts they were recorded with — nothing here is re-typed, corrected, or combined into an overall judgement about the part.

This record in the catalog: [DW254P-2X8-L0](/docs/components/catalog/#rec-dealon-dw254p-2x8-l0)

## Identity

| Field | Recorded value |
| --- | --- |
| Record ID | `rec-dealon-dw254p-2x8-l0` |
| Record kind | standalone |
| Manufacturer part number | `DW254P-2X8-L0` |
| Manufacturer | DEALON |
| Function | historical supply-side header candidate; not selected for the current EXT inlet |
| LCSC ID | `C4749189` |
| Package | `right-angle 2×8 through-hole header, 2.54 mm pitch` |
| Inventory line | `line-dealon-header` |
| Also known as | `supply-side power interconnect header` |
| Owner skill | `component-dealon-dw254p-2x8-l0` |

**Fit:** DNP or hand-fit

**Identity state:** UNRESOLVED

**Source state:** AVAILABLE

**Coverage:** 4 open of 4 published

## Documents and package

<EvidenceAnchor id="component-references-heading" />

<ComponentReferences descriptor="7b2276657273696f6e223a312c22646f63756d656e74223a7b226c6162656c223a2253706563696669636174696f6e20504446222c227469746c65223a224c435343204445414c4f4e204457323534502d3258382d4c30206c697374696e67222c22617574686f72697479223a224449535452494255544f525f4944454e54495459222c22617661696c6162696c697479223a22415641494c41424c45222c2275726c223a2268747470733a2f2f7777772e6c6373632e636f6d2f65732f70726f647563742d64657461696c2f4944432d436f6e6e6563746f72735f4445414c4f4e2d4457323534502d3258382d4c305f43343734393138392e68746d6c227d2c22666f6f747072696e74223a7b226e616d65223a224944432d54485f3136502d50322e35345f33323130313652473041424b3030413031222c22617373657455726c223a222f6173736574732f636f6d706f6e656e742d70726576696577732f666f6f747072696e74732f4944432d54485f3136502d50322e35345f33323130313652473041424b30304130312e737667227d2c226d6f64656c44657363726970746f72223a22376232323736363537323733363936663665323233613331326332323730363136333662363136373635343936343232336132323439343434333264353434383566333133363530326435303332326533353334356633333332333133303331333635323437333034313432346233303330343133303331323232633232373036313633366236313637363534633631363236353663323233613232343934343433326435343438356633313336353032643530333232653335333435663333333233313330333133363532343733303431343234623330333034313330333132323263323236643666363436353663353537323663323233613232326636313733373336353734373332663633366636643730366636653635366537343264373037323635373636393635373737333266366436663634363536633733326634393434343332643534343835663331333635303264353033323265333533343566333333323331333033313336353234373330343134323462333033303431333033313265373737323663323232633232366636363636373336353734323233613762323237383232336133303263323237393232336133303263323237613232336133303764326332323732366637343631373436393666366532323361376232323738323233613330326332323739323233613330326332323761323233613330376432633232373336333631366336353232336137623232373832323361333132633232373932323361333132633232376132323361333137643764227d" />

**Selected document:** [Specification PDF](https://www.lcsc.com/es/product-detail/IDC-Connectors_DEALON-DW254P-2X8-L0_C4749189.html) — LCSC DEALON DW254P-2X8-L0 listing

**Selected source ID:** `src-dealon-lcsc`

**Authority:** DISTRIBUTOR\_IDENTITY

**Availability:** AVAILABLE

**Package footprint:** `IDC-TH_16P-P2.54_321016RG0ABK00A01`

This geometry represents a shared footprint package and may not exactly match the manufacturer part.

## Placements

No board placement is published for this record.

## Coverage

Coverage is stated one domain at a time and is never rolled up. A domain marked open is a question that has not been answered; it is not a finding that the part is unsuitable. A record with no open domains has not thereby been declared safe.

### identity

<EvidenceAnchor id="cov-dealon-identity" />

**Coverage ID:** `cov-dealon-identity` · **Status:** OPEN

**Reason:** The supplier listing confirms the order identity, but the manufacturer fact has no manufacturer-primary source.

**Facts in this domain:**

- [`fact-dealon-identity`](#fact-dealon-identity)
- [`fact-dealon-manufacturer`](#fact-dealon-manufacturer)

**Blocked by:** these facts must be resolved before the domain can close. Each is listed in full under Facts.

- [`fact-dealon-manufacturer`](#fact-dealon-manufacturer)

### pinout

<EvidenceAnchor id="cov-dealon-pinout" />

**Coverage ID:** `cov-dealon-pinout` · **Status:** OPEN

**Reason:** Supply-side cable signals and net assignments have not been established.

**Facts in this domain:**

- [`fact-dealon-pinout`](#fact-dealon-pinout)

**Blocked by:** these facts must be resolved before the domain can close. Each is listed in full under Facts.

- [`fact-dealon-pinout`](#fact-dealon-pinout)

### mechanical\_fit

<EvidenceAnchor id="cov-dealon-mating" />

**Coverage ID:** `cov-dealon-mating` · **Status:** OPEN

**Reason:** Mating connector and retention require a physical check.

**Facts in this domain:**

- [`fact-dealon-mating-fit`](#fact-dealon-mating-fit)

**Blocked by:** these facts must be resolved before the domain can close. Each is listed in full under Facts.

- [`fact-dealon-mating-fit`](#fact-dealon-mating-fit)

### cad\_geometry

<EvidenceAnchor id="cov-dealon-cad" />

**Coverage ID:** `cov-dealon-cad` · **Status:** OPEN

**Reason:** The CAD asset remains family fidelity pending exact manufacturer drawing comparison.

**Facts in this domain:**

- [`fact-dealon-cad-fidelity`](#fact-dealon-cad-fidelity)

**Blocked by:** these facts must be resolved before the domain can close. Each is listed in full under Facts.

- [`fact-dealon-cad-fidelity`](#fact-dealon-cad-fidelity)

## Facts

Each fact keeps its value, its unit, the conditions it holds under, where it came from and how far it has been confirmed as separate fields, because they are separate claims. A value without its conditions is not the same fact, and a verdict is about the evidence for the value, not about the part.

### PROJECT\_STATE

A value this project recorded about how the part is used here — a chosen operating point, a net assignment, or a derived figure. Not a manufacturer specification.

<EvidenceFact>
  <EvidenceAnchor id="fact-dealon-identity" />

  **Fact:** `fact-dealon-identity`

  **Value:** `lcsc`=C4749189; `manufacturer`=DEALON; `mpn`=DW254P-2X8-L0; `variant`=Exact MPN and LCSC identity listing; right-angle 2×8 through-hole package. · **Unit:** `NONE`

  **Conditions:** Exact candidate in the unvalidated project draft.

  **Verdict:** CONFIRMED - distributor identity only · **Provenance:** DISTRIBUTOR-IDENTITY

  **Evidence:** [`src-dealon-lcsc`](#src-dealon-lcsc) — Identity section: Product heading and identity fields.
</EvidenceFact>

<EvidenceFact>
  <EvidenceAnchor id="fact-dealon-pinout" />

  **Fact:** `fact-dealon-pinout`

  **Value:** Supply-side cable pin functions and project net assignments are not established by the retained identity listing. · **Unit:** `NONE`

  **Conditions:** Exact candidate in the unvalidated project draft.

  **Verdict:** UNSOURCED · **Provenance:** UNVERIFIED

  **Evidence:** [`src-dealon-lcsc`](#src-dealon-lcsc) — Supplier pinout/footprint images are not retained as primary pin-map evidence; project cable assignment is absent.
</EvidenceFact>

<EvidenceFact>
  <EvidenceAnchor id="fact-dealon-mating-fit" />

  **Fact:** `fact-dealon-mating-fit`

  **Value:** Mating plug, latch/retention, cable keying and board-edge clearance have not been coupon-checked. · **Unit:** `NONE`

  **Conditions:** Exact candidate in the unvalidated project draft.

  **Verdict:** NEEDS BENCH · **Provenance:** PROJECT-CHOICE

  **Evidence:** [`src-dealon-lcsc`](#src-dealon-lcsc) — Identity section: No exact mating cable or assembled interconnect receipt is retained.
</EvidenceFact>

<EvidenceFact>
  <EvidenceAnchor id="fact-dealon-cad-fidelity" />

  **Fact:** `fact-dealon-cad-fidelity`

  **Value:** Existing footprint and 3D representation are package-family assets and have not been matched to an exact manufacturer drawing. · **Unit:** `NONE`

  **Conditions:** Exact candidate in the unvalidated project draft.

  **Verdict:** UNSOURCED · **Provenance:** UNVERIFIED

  **Evidence:** [`src-dealon-lcsc`](#src-dealon-lcsc) — Identity section: cad-c4749189-dw254p-2x8-l0 receipt classifies the CAD as family fidelity.
</EvidenceFact>

<EvidenceFact>
  <EvidenceAnchor id="fact-dealon-manufacturer" />

  **Fact:** `fact-dealon-manufacturer`

  **Value:** DEALON · **Unit:** `NONE`

  **Conditions:** Manufacturer identity for this exact candidate in the unvalidated project draft.

  **Verdict:** UNSOURCED · **Provenance:** UNVERIFIED

  **Evidence:** [`src-dealon-lcsc`](#src-dealon-lcsc) — Product identity section: distributor identifies the name, but no manufacturer-primary source is retained.
</EvidenceFact>

## Pin maps

The mapping between schematic pins and PCB pads, or physical terminals for an external part, as recorded. A record may carry more than one map when the same part is documented in more than one context.

### pinmap-dealon-header

<EvidenceAnchor id="pinmap-dealon-header" />

- **Symbol:** `DW254P-2X8-L0`
- **Footprint:** `IDC-TH_16P-P2.54_321016RG0ABK00A01`
- **Pins:** 16

<EvidenceDetails label="pin-assignments">
  <EvidenceTable label="pin-assignments">
    | Symbol pin | Name                                   | Footprint pad | Function                                                |
    | ---------- | -------------------------------------- | ------------- | ------------------------------------------------------- |
    | `1`        | `CONTACT_1 (pin function unverified)`  | `1`           | unverified interconnect contact; net assignment pending |
    | `2`        | `CONTACT_2 (pin function unverified)`  | `2`           | unverified interconnect contact; net assignment pending |
    | `3`        | `CONTACT_3 (pin function unverified)`  | `3`           | unverified interconnect contact; net assignment pending |
    | `4`        | `CONTACT_4 (pin function unverified)`  | `4`           | unverified interconnect contact; net assignment pending |
    | `5`        | `CONTACT_5 (pin function unverified)`  | `5`           | unverified interconnect contact; net assignment pending |
    | `6`        | `CONTACT_6 (pin function unverified)`  | `6`           | unverified interconnect contact; net assignment pending |
    | `7`        | `CONTACT_7 (pin function unverified)`  | `7`           | unverified interconnect contact; net assignment pending |
    | `8`        | `CONTACT_8 (pin function unverified)`  | `8`           | unverified interconnect contact; net assignment pending |
    | `9`        | `CONTACT_9 (pin function unverified)`  | `9`           | unverified interconnect contact; net assignment pending |
    | `10`       | `CONTACT_10 (pin function unverified)` | `10`          | unverified interconnect contact; net assignment pending |
    | `11`       | `CONTACT_11 (pin function unverified)` | `11`          | unverified interconnect contact; net assignment pending |
    | `12`       | `CONTACT_12 (pin function unverified)` | `12`          | unverified interconnect contact; net assignment pending |
    | `13`       | `CONTACT_13 (pin function unverified)` | `13`          | unverified interconnect contact; net assignment pending |
    | `14`       | `CONTACT_14 (pin function unverified)` | `14`          | unverified interconnect contact; net assignment pending |
    | `15`       | `CONTACT_15 (pin function unverified)` | `15`          | unverified interconnect contact; net assignment pending |
    | `16`       | `CONTACT_16 (pin function unverified)` | `16`          | unverified interconnect contact; net assignment pending |
  </EvidenceTable>
</EvidenceDetails>

## Interactions

Behaviour that is not a property of this part alone. Each interaction names the records it spans, the conditions it holds under, and how far it has been confirmed. An interaction that spans several parts appears on every one of their pages, under the same identifier, because it is equally a fact about each.

### int-dealon-supply

<EvidenceAnchor id="int-dealon-supply" />

- **Records involved:** `rec-dealon-dw254p-2x8-l0` (this record)
- **Conditions:** Retained historical supply-side header candidate, not selected for the current EXT inlet. No cable pin assignment, mating part, or system-level supply wiring is established by this component record.
- **Verdict:** UNSOURCED

**Facts this rests on:**

- [`fact-dealon-identity`](#fact-dealon-identity)
- [`fact-dealon-pinout`](#fact-dealon-pinout)
- [`fact-dealon-mating-fit`](#fact-dealon-mating-fit)
- [`fact-dealon-cad-fidelity`](#fact-dealon-cad-fidelity)

## Cross-component rules

Rules that span several parts at once and are published in full on the integration page. Each rule's verdict below is that rule's own — it is a statement about the cross-component question, not about this part — and the exact wording of what the rule refuses to conclude is published with the rule itself.

No cross-component rule names this record.

## Sources

Every document cited above, with its identification, when it was retrieved, and what kind of authority it carries. Sources that could not be retrieved are listed too, with their unavailability stated, so a gap in the evidence is visible rather than absent.

### LCSC DEALON DW254P-2X8-L0 listing

<EvidenceAnchor id="src-dealon-lcsc" />

**Source ID:** `src-dealon-lcsc` · **Authority:** DISTRIBUTOR\_IDENTITY

| Field | Recorded value |
| --- | --- |
| Document number | C4749189 |
| Revision | not stated in source |
| Document date | not stated in source |
| Retrieved | 2026-09-28 |
| Printed page | web page |

**Locator:** Identity section: Product heading and identity fields for DEALON MPN DW254P-2X8-L0, LCSC C4749189; listing shows right-angle 2×8, 2.54 mm.

**Availability:** AVAILABLE

**Document URL:** [https://www.lcsc.com/es/product-detail/IDC-Connectors\_DEALON-DW254P-2X8-L0\_C4749189.html](https://www.lcsc.com/es/product-detail/IDC-Connectors_DEALON-DW254P-2X8-L0_C4749189.html)

## Legend

What the recorded terms on this page mean, in ordinary words. The exact terms above are the ones that count; these descriptions explain them and never replace them.

### Verdict

| Recorded term | What it means |
| --- | --- |
| `CONFIRMED - distributor identity only` | A distributor listing confirms which part this is, and nothing more. It carries no electrical, thermal or lifetime authority. |
| `NEEDS BENCH` | Cannot be settled from documents. It needs measurement on real hardware before it can be relied on. |
| `UNSOURCED` | No accepted source backs this value yet. Treat it as a claim, not a fact. |

### Provenance

| Recorded term | What it means |
| --- | --- |
| `DISTRIBUTOR-IDENTITY` | Taken from a distributor listing. Identity information only. |
| `PROJECT-CHOICE` | A decision made by this project. No vendor asserts it. |
| `UNVERIFIED` | Recorded, but not yet backed by an accepted source. |

### Fact class

| Recorded term | What it means |
| --- | --- |
| `PROJECT_STATE` | A value this project recorded about how the part is used here — a chosen operating point, a net assignment, or a derived figure. Not a manufacturer specification. |

### Coverage status

| Recorded term | What it means |
| --- | --- |
| `OPEN` | Unresolved. Open means the question has not been answered, not that the part is unsafe — the reason states what is missing. |

### Source availability

| Recorded term | What it means |
| --- | --- |
| `AVAILABLE` | The document was retrieved and is on record. |

### Source authority

| Recorded term | What it means |
| --- | --- |
| `DISTRIBUTOR_IDENTITY` | A distributor listing. Establishes which part this is, nothing more. |

### Identity state

| Recorded term | What it means |
| --- | --- |
| `UNRESOLVED`  | The exact orderable part is not yet confirmed. Substituting a same-name part from another vendor is not permitted on that basis. |

### Source state

| Recorded term | What it means |
| --- | --- |
| `AVAILABLE` | At least one document backing this line was retrieved. |

### Unit

| Recorded term | What it means |
| --- | --- |
| `NONE` | The value is not a physical quantity, so it carries no unit. Recorded as \`NONE\`. |

## Raw agent resource

This page is generated from a stored evidence bundle and does not restate it. The bundle is the source of truth: where the two ever disagree, the bundle is right and this page is stale.

[Open the owning bundle](/docs/claude-skills/component-dealon-dw254p-2x8-l0/) `component-dealon-dw254p-2x8-l0`
