Takazudo/zudo-osc-hole-field/doc/src/content/docs/components/records/clamp-diode/index.mdx

---
# GENERATED by @takazudo/zudo-circuit-doc — do not edit; run `zudo-circuit-doc generate`
title: "BAT54S,215"
description: "rail clamp pair — Nexperia — no placement published — rec-clamp-diode"
sidebar_position: 28
---

<EvidenceAnchor id="rec-clamp-diode" />

Generated from the component evidence records — edit the records, not this page.

Everything below is projected from this project's stored component evidence. Values keep the exact wording, conditions, units and verdicts they were recorded with — nothing here is re-typed, corrected, or combined into an overall judgement about the part.

This record in the catalog: [BAT54S,215](/docs/components/catalog/#rec-clamp-diode)

## Identity

| Field | Recorded value |
| --- | --- |
| Record ID | `rec-clamp-diode` |
| Record kind | standalone |
| Manufacturer part number | `BAT54S,215` |
| Manufacturer | Nexperia |
| Function | rail clamp pair |
| LCSC ID | Not assigned; order by exact manufacturer part number |
| Package | `SOT-23` |
| Inventory line | `line-clamp-diode` |
| Owner skill | `component-nexperia-bat54s-215` |

**Fit:** Fitted

**Identity state:** VERIFIED

**Source state:** AVAILABLE

**Coverage:** 3 open of 6 published

## Documents and package

<EvidenceAnchor id="component-references-heading" />

<ComponentReferences descriptor="7b2276657273696f6e223a312c22646f63756d656e74223a7b226c6162656c223a2244617461736865657420504446222c227469746c65223a225363686f74746b7920626172726965722064696f646573222c22617574686f72697479223a224d414e5546414354555245525f5052494d415259222c22617661696c6162696c697479223a22415641494c41424c45222c2275726c223a2268747470733a2f2f6173736574732e6e657870657269612e636f6d2f646f63756d656e74732f646174612d73686565742f4241543534532e706466227d2c22666f6f747072696e74223a7b226e616d65223a22534f542d3233222c22617373657455726c223a222f6173736574732f636f6d706f6e656e742d70726576696577732f666f6f747072696e74732f534f542d32332e737667227d2c226d6f64656c44657363726970746f72223a22376232323736363537323733363936663665323233613331326332323730363136333662363136373635343936343232336132323533346635343264333233333232326332323730363136333662363136373635346336313632363536633232336132323533346635343264333233333232326332323664366636343635366335353732366332323361323232663631373337333635373437333266363336663664373036663665363536653734326437303732363537363639363537373733326636643666363436353663373332663439343335663533346635343264333233333265373737323663323232633232366636363636373336353734323233613762323237383232336133303263323237393232336133303263323237613232336133303764326332323732366637343631373436393666366532323361376232323738323233613330326332323739323233613330326332323761323233613330376432633232373336333631366336353232336137623232373832323361333132633232373932323361333132633232376132323361333137643764227d" />

**Selected document:** [Datasheet PDF](https://assets.nexperia.com/documents/data-sheet/BAT54S.pdf) — Schottky barrier diodes

**Selected source ID:** `src-clamp-diode-datasheet`

**Authority:** MANUFACTURER\_PRIMARY

**Availability:** AVAILABLE

**Package footprint:** `SOT-23`

This geometry represents a shared footprint package and may not exactly match the manufacturer part.

## Placements

No board placement is published for this record.

## Coverage

Coverage is stated one domain at a time and is never rolled up. A domain marked open is a question that has not been answered; it is not a finding that the part is unsuitable. A record with no open domains has not thereby been declared safe.

### exact orderable identity

<EvidenceAnchor id="cov-clamp-diode-exact-orderable-identity" />

**Coverage ID:** `cov-clamp-diode-exact-orderable-identity` · **Status:** OPEN

**Reason:** The current exact MPN is a project-selected proposal but its full manufacturer orderable identity/package suffix is not confirmed by retained exact-part bytes.

**Facts in this domain:**

- [`fact-clamp-diode-orderable-identity`](#fact-clamp-diode-orderable-identity)

**Blocked by:** these facts must be resolved before the domain can close. Each is listed in full under Facts.

- [`fact-clamp-diode-orderable-identity`](#fact-clamp-diode-orderable-identity)

### pinout

<EvidenceAnchor id="cov-clamp-diode-pinout" />

**Coverage ID:** `cov-clamp-diode-pinout` · **Status:** COVERED

**Reason:** The retained manufacturer document provides the listed pin-function table; no project nets are assigned.

**Facts in this domain:**

- [`fact-clamp-diode-pinout`](#fact-clamp-diode-pinout)

### electrical limits

<EvidenceAnchor id="cov-clamp-diode-electrical-limits" />

**Coverage ID:** `cov-clamp-diode-electrical-limits` · **Status:** COVERED

**Reason:** Retained source supports the specific listed product-family limits; conditions remain attached to each fact.

**Facts in this domain:**

- [`fact-clamp-diode-reverse-voltage`](#fact-clamp-diode-reverse-voltage)

### manufacturer product description

<EvidenceAnchor id="cov-clamp-diode-manufacturer-product-description" />

**Coverage ID:** `cov-clamp-diode-manufacturer-product-description` · **Status:** COVERED

**Reason:** The retained manufacturer document identifies the named product and its documented role/description; this is not application qualification.

**Facts in this domain:**

- [`fact-clamp-diode-product-function`](#fact-clamp-diode-product-function)

### mechanical fit

<EvidenceAnchor id="cov-clamp-diode-mechanical-fit" />

**Coverage ID:** `cov-clamp-diode-mechanical-fit` · **Status:** OPEN

**Reason:** The local family envelope and generic footprint are provisional; physical board fit and land-pattern suitability are not validated.

**Facts in this domain:**

- [`fact-clamp-diode-mechanical-fit`](#fact-clamp-diode-mechanical-fit)

**Blocked by:** these facts must be resolved before the domain can close. Each is listed in full under Facts.

- [`fact-clamp-diode-mechanical-fit`](#fact-clamp-diode-mechanical-fit)

### procurement

<EvidenceAnchor id="cov-clamp-diode-procurement" />

**Coverage ID:** `cov-clamp-diode-procurement` · **Status:** OPEN

**Reason:** Supplier stock, lead time, consignment and assembly allocation remain unverified as of the dated shortlist.

**Facts in this domain:**

- [`fact-clamp-diode-procurement-status`](#fact-clamp-diode-procurement-status)

**Blocked by:** these facts must be resolved before the domain can close. Each is listed in full under Facts.

- [`fact-clamp-diode-procurement-status`](#fact-clamp-diode-procurement-status)

## Facts

Each fact keeps its value, its unit, the conditions it holds under, where it came from and how far it has been confirmed as separate fields, because they are separate claims. A value without its conditions is not the same fact, and a verdict is about the evidence for the value, not about the part.

### GUARANTEED\_ELECTRICAL

A parameter the manufacturer guarantees over the stated conditions, usually with minimum, typical and maximum values.

<EvidenceFact>
  <EvidenceAnchor id="fact-clamp-diode-reverse-voltage" />

  **Fact:** `fact-clamp-diode-reverse-voltage`

  **Value:** `maximum`=30 · **Unit:** `V`

  **Conditions:** BAT54S Schottky diode; manufacturer quick-reference table.

  **Verdict:** PASS - primary-source confirmed · **Provenance:** PRIMARY-SPEC

  **Evidence:** [src-clamp-diode-datasheet: PDF page index 0, printed page 1, Table 1, reverse voltage VR row](#src-clamp-diode-datasheet)
</EvidenceFact>

### PROJECT\_STATE

A value this project recorded about how the part is used here — a chosen operating point, a net assignment, or a derived figure. Not a manufacturer specification.

<EvidenceFact>
  <EvidenceAnchor id="fact-clamp-diode-manufacturer" />

  **Fact:** `fact-clamp-diode-manufacturer`

  **Value:** Nexperia · **Unit:** `NONE`

  **Conditions:** Manufacturer of the project-selected exact shortlist identity.

  **Verdict:** PASS - primary-source confirmed · **Provenance:** PRIMARY-SPEC

  **Evidence:** [src-clamp-diode-datasheet: title block or OSC-ES-1 row parts\[id=clamp\_diode\].manufacturer](#src-clamp-diode-datasheet)
</EvidenceFact>

<EvidenceFact>
  <EvidenceAnchor id="fact-clamp-diode-project-selection" />

  **Fact:** `fact-clamp-diode-project-selection`

  **Value:** `lcsc`=not listed in the shortlist; `manufacturer`=Nexperia; `mpn`=BAT54S,215; `package`=SOT-23; `roles`=rail clamp pair; `source_status`=UNVERIFIED · **Unit:** `NONE`

  **Conditions:** OSC-ES-1 dated proposal row; exact source status and availability statements are not supplier allocation.

  **Verdict:** NOT APPLICABLE · **Provenance:** PROJECT-CHOICE

  **Evidence:** [src-clamp-diode-shortlist: JSON row parts\[id=clamp\_diode\]](#src-clamp-diode-shortlist)
</EvidenceFact>

<EvidenceFact>
  <EvidenceAnchor id="fact-clamp-diode-orderable-identity" />

  **Fact:** `fact-clamp-diode-orderable-identity`

  **Value:** `manufacturer`=Nexperia; `mpn`=BAT54S,215; `package`=SOT-23 · **Unit:** `NONE`

  **Conditions:** Exact complete orderable identifier in the selected package; does not establish supplier stock.

  **Verdict:** UNSOURCED · **Provenance:** UNVERIFIED

  **Evidence:** [Section/table audit: src-clamp-diode-datasheet: retained source does not establish complete exact MPN BAT54S,215; see project shortlist selection](#src-clamp-diode-datasheet)
</EvidenceFact>

<EvidenceFact>
  <EvidenceAnchor id="fact-clamp-diode-pinout" />

  **Fact:** `fact-clamp-diode-pinout`

  **Value:** pin 1 A1 anode diode 1 -> pad 1; pin 2 K2 cathode diode 2 -> pad 2; pin 3 K1/A2 series common -> pad 3 · **Unit:** `NONE`

  **Conditions:** No schematic or placement/net binding is claimed. Manufacturer pin functions are source-backed only when a retained primary document names the product family.

  **Verdict:** PASS - primary-source confirmed · **Provenance:** PRIMARY-SPEC

  **Evidence:** [src-clamp-diode-datasheet: Pin configuration/function table](#src-clamp-diode-datasheet)
</EvidenceFact>

<EvidenceFact>
  <EvidenceAnchor id="fact-clamp-diode-product-function" />

  **Fact:** `fact-clamp-diode-product-function`

  **Value:** Manufacturer source identifies BAT54S,215 as the shortlisted rail clamp pair device; this is not project suitability. · **Unit:** `NONE`

  **Conditions:** Product family description only; no project application or electrical guarantee implied.

  **Verdict:** PASS - primary-source confirmed · **Provenance:** PRIMARY-SPEC

  **Evidence:** [src-clamp-diode-datasheet: document title block and product description](#src-clamp-diode-datasheet)
</EvidenceFact>

<EvidenceFact>
  <EvidenceAnchor id="fact-clamp-diode-procurement-status" />

  **Fact:** `fact-clamp-diode-procurement-status`

  **Value:** UNVERIFIED · **Unit:** `NONE`

  **Conditions:** Time-stamped OSC-ES-1 state on 2026-09-28; current stock, lead time, consignment, and JLC assembly are not established.

  **Verdict:** UNSOURCED · **Provenance:** PROJECT-CHOICE

  **Evidence:** [src-clamp-diode-shortlist: JSON row parts\[id=clamp\_diode\].sourcing.status/jlcpcb\_assembly](#src-clamp-diode-shortlist)
</EvidenceFact>

<EvidenceFact>
  <EvidenceAnchor id="fact-clamp-diode-mechanical-fit" />

  **Fact:** `fact-clamp-diode-mechanical-fit`

  **Value:** Provisional package-family envelope only; board/land-pattern fit has not been physically checked. · **Unit:** `NONE`

  **Conditions:** Selected footprint family and display envelope do not establish exact-part placement or solderability.

  **Verdict:** NEEDS BENCH · **Provenance:** PROJECT-CHOICE

  **Evidence:** [Section/table audit: src-clamp-diode-shortlist: parts\[id=clamp\_diode\].package; CAD receipt is provisional family geometry](#src-clamp-diode-shortlist)
</EvidenceFact>

## Pin maps

The mapping between schematic pins and PCB pads, or physical terminals for an external part, as recorded. A record may carry more than one map when the same part is documented in more than one context.

### pinmap-clamp-diode

<EvidenceAnchor id="pinmap-clamp-diode" />

- **Symbol:** `BAT54S_215`
- **Footprint:** `SOT-23`
- **Pins:** 3

<EvidenceDetails label="pin-assignments">
  <EvidenceTable label="pin-assignments">
    | Symbol pin | Name                  | Footprint pad | Function            |
    | ---------- | --------------------- | ------------- | ------------------- |
    | `1`        | `A1 anode diode 1`    | `1`           | A1 anode diode 1    |
    | `2`        | `K2 cathode diode 2`  | `2`           | K2 cathode diode 2  |
    | `3`        | `K1/A2 series common` | `3`           | K1/A2 series common |
  </EvidenceTable>
</EvidenceDetails>

## Interactions

Behaviour that is not a property of this part alone. Each interaction names the records it spans, the conditions it holds under, and how far it has been confirmed. An interaction that spans several parts appears on every one of their pages, under the same identifier, because it is equally a fact about each.

### int-clamp-diode-project-role

<EvidenceAnchor id="int-clamp-diode-project-role" />

- **Records involved:** `rec-clamp-diode` (this record)
- **Conditions:** Project role from OSC-ES-1; schematic nets, board placements, pin assignment and circuit behavior remain unbound.
- **Verdict:** NEEDS BENCH

**Facts this rests on:**

- [`fact-clamp-diode-project-selection`](#fact-clamp-diode-project-selection)
- [`fact-clamp-diode-pinout`](#fact-clamp-diode-pinout)

## Cross-component rules

Rules that span several parts at once and are published in full on the integration page. Each rule's verdict below is that rule's own — it is a statement about the cross-component question, not about this part — and the exact wording of what the rule refuses to conclude is published with the rule itself.

No cross-component rule names this record.

## Sources

Every document cited above, with its identification, when it was retrieved, and what kind of authority it carries. Sources that could not be retrieved are listed too, with their unavailability stated, so a gap in the evidence is visible rather than absent.

### Schottky barrier diodes

<EvidenceAnchor id="src-clamp-diode-datasheet" />

**Source ID:** `src-clamp-diode-datasheet` · **Authority:** MANUFACTURER\_PRIMARY

| Field | Recorded value |
| --- | --- |
| Document number | BAT54S |
| Revision | v.6 |
| Document date | 1 July 2022 |
| Retrieved | 2026-09-28 |
| Printed page | 1 |

**Locator:** Pin configuration/function table

**Availability:** AVAILABLE

**Document URL:** [https://assets.nexperia.com/documents/data-sheet/BAT54S.pdf](https://assets.nexperia.com/documents/data-sheet/BAT54S.pdf)

### OSC-ES-1 parts shortlist

<EvidenceAnchor id="src-clamp-diode-shortlist" />

**Source ID:** `src-clamp-diode-shortlist` · **Authority:** PROJECT\_GENERATOR

| Field | Recorded value |
| --- | --- |
| Document number | OSC-ES-1 |
| Revision | base SHA b185391d30ec38293bc6c5e8b798a282b98baa25 |
| Document date | 2026-09-28 |
| Retrieved | 2026-09-28 |
| Printed page | not paginated |

**Locator:** JSON row parts\[id=clamp\_diode], fields manufacturer/mpn/package/lcsc/sourcing

**Availability:** AVAILABLE

**Document URL:** [https://github.com/Takazudo/zudo-osc-hole-field/blob/base/osc-hole-field/design/standard/parts-shortlist.json](https://github.com/Takazudo/zudo-osc-hole-field/blob/base/osc-hole-field/design/standard/parts-shortlist.json)

## Legend

What the recorded terms on this page mean, in ordinary words. The exact terms above are the ones that count; these descriptions explain them and never replace them.

### Verdict

| Recorded term | What it means |
| --- | --- |
| `NEEDS BENCH` | Cannot be settled from documents. It needs measurement on real hardware before it can be relied on. |
| `NOT APPLICABLE` | The parameter does not apply to this part as it is used here. |
| `PASS - primary-source confirmed` | Confirmed against the manufacturer's own document for this exact part. |
| `UNSOURCED` | No accepted source backs this value yet. Treat it as a claim, not a fact. |

### Provenance

| Recorded term | What it means |
| --- | --- |
| `PRIMARY-SPEC` | Taken from the manufacturer's own specification document. |
| `PROJECT-CHOICE` | A decision made by this project. No vendor asserts it. |
| `UNVERIFIED` | Recorded, but not yet backed by an accepted source. |

### Fact class

| Recorded term | What it means |
| --- | --- |
| `GUARANTEED_ELECTRICAL` | A parameter the manufacturer guarantees over the stated conditions, usually with minimum, typical and maximum values. |
| `PROJECT_STATE` | A value this project recorded about how the part is used here — a chosen operating point, a net assignment, or a derived figure. Not a manufacturer specification. |

### Coverage status

| Recorded term | What it means |
| --- | --- |
| `COVERED` | Every question this domain asks is answered by the facts listed against it. |
| `OPEN` | Unresolved. Open means the question has not been answered, not that the part is unsafe — the reason states what is missing. |

### Source availability

| Recorded term | What it means |
| --- | --- |
| `AVAILABLE` | The document was retrieved and is on record. |

### Source authority

| Recorded term | What it means |
| --- | --- |
| `MANUFACTURER_PRIMARY` | The manufacturer's own document for this exact part. |
| `PROJECT_GENERATOR` | A document this project generated, such as a schematic or netlist export. |

### Identity state

| Recorded term | What it means |
| --- | --- |
| `VERIFIED` | The exact orderable part has been confirmed against a source. |

### Source state

| Recorded term | What it means |
| --- | --- |
| `AVAILABLE` | At least one document backing this line was retrieved. |

### Unit

| Recorded term | What it means |
| --- | --- |
| `NONE` | The value is not a physical quantity, so it carries no unit. Recorded as \`NONE\`. |

## Raw agent resource

This page is generated from a stored evidence bundle and does not restate it. The bundle is the source of truth: where the two ever disagree, the bundle is right and this page is stale.

[Open the owning bundle](/docs/claude-skills/component-nexperia-bat54s-215/) `component-nexperia-bat54s-215`
