Takazudo/zudo-osc-hole-field/doc/src/content/docs/components/records/comparator/index.mdx

---
# GENERATED by @takazudo/zudo-circuit-doc — do not edit; run `zudo-circuit-doc generate`
title: "LM393BIDR"
description: "gate; clip; envelope comparator — Texas Instruments — no placement published — rec-comparator"
sidebar_position: 16
---

<EvidenceAnchor id="rec-comparator" />

Generated from the component evidence records — edit the records, not this page.

Everything below is projected from this project's stored component evidence. Values keep the exact wording, conditions, units and verdicts they were recorded with — nothing here is re-typed, corrected, or combined into an overall judgement about the part.

This record in the catalog: [LM393BIDR](/docs/components/catalog/#rec-comparator)

## Identity

| Field | Recorded value |
| --- | --- |
| Record ID | `rec-comparator` |
| Record kind | standalone |
| Manufacturer part number | `LM393BIDR` |
| Manufacturer | Texas Instruments |
| Function | gate; clip; envelope comparator |
| LCSC ID | Not assigned; order by exact manufacturer part number |
| Package | `SOIC-8` |
| Inventory line | `line-comparator` |
| Also known as | `gate`, `clip`, `envelope comparator` |
| Owner skill | `component-ti-lm393bidr` |

**Fit:** Fitted

**Identity state:** VERIFIED

**Source state:** AVAILABLE

**Coverage:** 2 open of 6 published

## Documents and package

<EvidenceAnchor id="component-references-heading" />

<ComponentReferences descriptor="7b2276657273696f6e223a312c22646f63756d656e74223a7b226c6162656c223a2244617461736865657420504446222c227469746c65223a224c4d333933422c204c4d32393033422c204c4d3139332c204c4d3239332c204c4d33393320616e64204c4d32393033204475616c20436f6d70617261746f72732064617461736865657420285265762e20414829222c22617574686f72697479223a224d414e5546414354555245525f5052494d415259222c22617661696c6162696c697479223a22415641494c41424c45222c2275726c223a2268747470733a2f2f7777772e74692e636f6d2f6c69742f64732f73796d6c696e6b2f6c6d333933622e706466227d2c22666f6f747072696e74223a7b226e616d65223a22534f49432d385f332e3978342e396d6d5f50312e32376d6d222c22617373657455726c223a222f6173736574732f636f6d706f6e656e742d70726576696577732f666f6f747072696e74732f534f49432d385f332e3978342e396d6d5f50312e32376d6d2e737667227d2c226d6f64656c44657363726970746f72223a2237623232373636353732373336393666366532323361333132633232373036313633366236313637363534393634323233613232353334663439343332643338356633333265333937383334326533393664366435663530333132653332333736643664323232633232373036313633366236313637363534633631363236353663323233613232353334663439343332643338356633333265333937383334326533393664366435663530333132653332333736643664323232633232366436663634363536633535373236633232336132323266363137333733363537343733326636333666366437303666366536353665373432643730373236353736363936353737373332663664366636343635366337333266343934333566353334663439343332643338356633333265333937383334326533393265373737323663323232633232366636363636373336353734323233613762323237383232336133303263323237393232336133303263323237613232336133303764326332323732366637343631373436393666366532323361376232323738323233613330326332323739323233613330326332323761323233613330376432633232373336333631366336353232336137623232373832323361333132633232373932323361333132633232376132323361333137643764227d" />

**Selected document:** [Datasheet PDF](https://www.ti.com/lit/ds/symlink/lm393b.pdf) — LM393B, LM2903B, LM193, LM293, LM393 and LM2903 Dual Comparators datasheet (Rev. AH)

**Selected source ID:** `src-comparator-datasheet`

**Authority:** MANUFACTURER\_PRIMARY

**Availability:** AVAILABLE

**Package footprint:** `SOIC-8_3.9x4.9mm_P1.27mm`

This geometry represents a shared footprint package and may not exactly match the manufacturer part.

## Placements

No board placement is published for this record.

## Coverage

Coverage is stated one domain at a time and is never rolled up. A domain marked open is a question that has not been answered; it is not a finding that the part is unsuitable. A record with no open domains has not thereby been declared safe.

### exact orderable identity

<EvidenceAnchor id="cov-comparator-exact-orderable-identity" />

**Coverage ID:** `cov-comparator-exact-orderable-identity` · **Status:** COVERED

**Reason:** Manufacturer primary bytes identify the exact shortlist MPN/package; supplier stock remains separately open.

**Facts in this domain:**

- [`fact-comparator-orderable-identity`](#fact-comparator-orderable-identity)

### pinout

<EvidenceAnchor id="cov-comparator-pinout" />

**Coverage ID:** `cov-comparator-pinout` · **Status:** COVERED

**Reason:** The retained manufacturer document provides the listed pin-function table; no project nets are assigned.

**Facts in this domain:**

- [`fact-comparator-pinout`](#fact-comparator-pinout)

### electrical limits

<EvidenceAnchor id="cov-comparator-electrical-limits" />

**Coverage ID:** `cov-comparator-electrical-limits` · **Status:** COVERED

**Reason:** Retained source supports the specific listed product-family limits; conditions remain attached to each fact.

**Facts in this domain:**

- [`fact-comparator-input-offset-voltage`](#fact-comparator-input-offset-voltage)
- [`fact-comparator-input-bias-current`](#fact-comparator-input-bias-current)

### manufacturer product description

<EvidenceAnchor id="cov-comparator-manufacturer-product-description" />

**Coverage ID:** `cov-comparator-manufacturer-product-description` · **Status:** COVERED

**Reason:** The retained manufacturer document identifies the named product and its documented role/description; this is not application qualification.

**Facts in this domain:**

- [`fact-comparator-product-function`](#fact-comparator-product-function)

### mechanical fit

<EvidenceAnchor id="cov-comparator-mechanical-fit" />

**Coverage ID:** `cov-comparator-mechanical-fit` · **Status:** OPEN

**Reason:** The local family envelope and generic footprint are provisional; physical board fit and land-pattern suitability are not validated.

**Facts in this domain:**

- [`fact-comparator-mechanical-fit`](#fact-comparator-mechanical-fit)

**Blocked by:** these facts must be resolved before the domain can close. Each is listed in full under Facts.

- [`fact-comparator-mechanical-fit`](#fact-comparator-mechanical-fit)

### procurement

<EvidenceAnchor id="cov-comparator-procurement" />

**Coverage ID:** `cov-comparator-procurement` · **Status:** OPEN

**Reason:** Supplier stock, lead time, consignment and assembly allocation remain unverified as of the dated shortlist.

**Facts in this domain:**

- [`fact-comparator-procurement-status`](#fact-comparator-procurement-status)

**Blocked by:** these facts must be resolved before the domain can close. Each is listed in full under Facts.

- [`fact-comparator-procurement-status`](#fact-comparator-procurement-status)

## Facts

Each fact keeps its value, its unit, the conditions it holds under, where it came from and how far it has been confirmed as separate fields, because they are separate claims. A value without its conditions is not the same fact, and a verdict is about the evidence for the value, not about the part.

### GUARANTEED\_ELECTRICAL

A parameter the manufacturer guarantees over the stated conditions, usually with minimum, typical and maximum values.

<EvidenceFact>
  <EvidenceAnchor id="fact-comparator-input-offset-voltage" />

  **Fact:** `fact-comparator-input-offset-voltage`

  **Value:** `maximum_at_25C`=2.5; `maximum_full_temperature`=4; `typical_at_25C`=0.37 · **Unit:** `mV`

  **Conditions:** TA = 25 C typ/max; TA = -40..85 C full-temperature maximum; LM393B electrical-characteristics table.

  **Verdict:** PASS - primary-source confirmed · **Provenance:** PRIMARY-SPEC

  **Evidence:** [src-comparator-datasheet: PDF page index 5, printed page 6, Electrical Characteristics, input offset voltage row](#src-comparator-datasheet)
</EvidenceFact>

<EvidenceFact>
  <EvidenceAnchor id="fact-comparator-input-bias-current" />

  **Fact:** `fact-comparator-input-bias-current`

  **Value:** `maximum_at_25C`=25; `maximum_full_temperature`=50; `typical_at_25C`=3.5 · **Unit:** `nA`

  **Conditions:** TA = 25 C typ/max; TA = -40..85 C full-temperature maximum; LM393B electrical-characteristics table.

  **Verdict:** PASS - primary-source confirmed · **Provenance:** PRIMARY-SPEC

  **Evidence:** [src-comparator-datasheet: PDF page index 5, printed page 6, Electrical Characteristics, input bias current row](#src-comparator-datasheet)
</EvidenceFact>

### PROJECT\_STATE

A value this project recorded about how the part is used here — a chosen operating point, a net assignment, or a derived figure. Not a manufacturer specification.

<EvidenceFact>
  <EvidenceAnchor id="fact-comparator-manufacturer" />

  **Fact:** `fact-comparator-manufacturer`

  **Value:** Texas Instruments · **Unit:** `NONE`

  **Conditions:** Manufacturer of the project-selected exact shortlist identity.

  **Verdict:** PASS - primary-source confirmed · **Provenance:** PRIMARY-SPEC

  **Evidence:** [src-comparator-datasheet: title block or OSC-ES-1 row parts\[id=comparator\].manufacturer](#src-comparator-datasheet)
</EvidenceFact>

<EvidenceFact>
  <EvidenceAnchor id="fact-comparator-project-selection" />

  **Fact:** `fact-comparator-project-selection`

  **Value:** `lcsc`=not listed in the shortlist; `manufacturer`=Texas Instruments; `mpn`=LM393BIDR; `package`=SOIC-8; `roles`=gate, clip, envelope comparator; `source_status`=UNVERIFIED · **Unit:** `NONE`

  **Conditions:** OSC-ES-1 dated proposal row; exact source status and availability statements are not supplier allocation.

  **Verdict:** NOT APPLICABLE · **Provenance:** PROJECT-CHOICE

  **Evidence:** [src-comparator-shortlist: JSON row parts\[id=comparator\]](#src-comparator-shortlist)
</EvidenceFact>

<EvidenceFact>
  <EvidenceAnchor id="fact-comparator-orderable-identity" />

  **Fact:** `fact-comparator-orderable-identity`

  **Value:** `manufacturer`=Texas Instruments; `mpn`=LM393BIDR; `package`=SOIC-8 · **Unit:** `NONE`

  **Conditions:** Exact complete orderable identifier in the selected package; does not establish supplier stock.

  **Verdict:** PASS - primary-source confirmed · **Provenance:** PRIMARY-SPEC

  **Evidence:** [Section/table audit: src-comparator-datasheet: package/orderable addendum names exact MPN](#src-comparator-datasheet)
</EvidenceFact>

<EvidenceFact>
  <EvidenceAnchor id="fact-comparator-pinout" />

  **Fact:** `fact-comparator-pinout`

  **Value:** pin 1 1OUT open collector -> pad 1; pin 2 1IN- -> pad 2; pin 3 1IN+ -> pad 3; pin 4 GND -> pad 4; pin 5 2IN+ -> pad 5; pin 6 2IN- -> pad 6; pin 7 2OUT open collector -> pad 7; pin 8 VCC -> pad 8 · **Unit:** `NONE`

  **Conditions:** No schematic or placement/net binding is claimed. Manufacturer pin functions are source-backed only when a retained primary document names the product family.

  **Verdict:** PASS - primary-source confirmed · **Provenance:** PRIMARY-SPEC

  **Evidence:** [src-comparator-datasheet: Pin configuration/function table](#src-comparator-datasheet)
</EvidenceFact>

<EvidenceFact>
  <EvidenceAnchor id="fact-comparator-product-function" />

  **Fact:** `fact-comparator-product-function`

  **Value:** Manufacturer source identifies LM393BIDR as the shortlisted gate, clip, envelope comparator device; this is not project suitability. · **Unit:** `NONE`

  **Conditions:** Product family description only; no project application or electrical guarantee implied.

  **Verdict:** PASS - primary-source confirmed · **Provenance:** PRIMARY-SPEC

  **Evidence:** [src-comparator-datasheet: document title block and product description](#src-comparator-datasheet)
</EvidenceFact>

<EvidenceFact>
  <EvidenceAnchor id="fact-comparator-procurement-status" />

  **Fact:** `fact-comparator-procurement-status`

  **Value:** UNVERIFIED · **Unit:** `NONE`

  **Conditions:** Time-stamped OSC-ES-1 state on 2026-09-28; current stock, lead time, consignment, and JLC assembly are not established.

  **Verdict:** UNSOURCED · **Provenance:** PROJECT-CHOICE

  **Evidence:** [src-comparator-shortlist: JSON row parts\[id=comparator\].sourcing.status/jlcpcb\_assembly](#src-comparator-shortlist)
</EvidenceFact>

<EvidenceFact>
  <EvidenceAnchor id="fact-comparator-mechanical-fit" />

  **Fact:** `fact-comparator-mechanical-fit`

  **Value:** Provisional package-family envelope only; board/land-pattern fit has not been physically checked. · **Unit:** `NONE`

  **Conditions:** Selected footprint family and display envelope do not establish exact-part placement or solderability.

  **Verdict:** NEEDS BENCH · **Provenance:** PROJECT-CHOICE

  **Evidence:** [Section/table audit: src-comparator-shortlist: parts\[id=comparator\].package; CAD receipt is provisional family geometry](#src-comparator-shortlist)
</EvidenceFact>

## Pin maps

The mapping between schematic pins and PCB pads, or physical terminals for an external part, as recorded. A record may carry more than one map when the same part is documented in more than one context.

### pinmap-comparator

<EvidenceAnchor id="pinmap-comparator" />

- **Symbol:** `LM393BIDR`
- **Footprint:** `SOIC-8_3.9x4.9mm_P1.27mm`
- **Pins:** 8

<EvidenceDetails label="pin-assignments">
  <EvidenceTable label="pin-assignments">
    | Symbol pin | Name                  | Footprint pad | Function            |
    | ---------- | --------------------- | ------------- | ------------------- |
    | `1`        | `1OUT open collector` | `1`           | 1OUT open collector |
    | `2`        | `1IN-`                | `2`           | 1IN-                |
    | `3`        | `1IN+`                | `3`           | 1IN+                |
    | `4`        | `GND`                 | `4`           | GND                 |
    | `5`        | `2IN+`                | `5`           | 2IN+                |
    | `6`        | `2IN-`                | `6`           | 2IN-                |
    | `7`        | `2OUT open collector` | `7`           | 2OUT open collector |
    | `8`        | `VCC`                 | `8`           | VCC                 |
  </EvidenceTable>
</EvidenceDetails>

## Interactions

Behaviour that is not a property of this part alone. Each interaction names the records it spans, the conditions it holds under, and how far it has been confirmed. An interaction that spans several parts appears on every one of their pages, under the same identifier, because it is equally a fact about each.

### int-comparator-project-role

<EvidenceAnchor id="int-comparator-project-role" />

- **Records involved:** `rec-comparator` (this record)
- **Conditions:** Project role from OSC-ES-1; schematic nets, board placements, pin assignment and circuit behavior remain unbound.
- **Verdict:** NEEDS BENCH

**Facts this rests on:**

- [`fact-comparator-project-selection`](#fact-comparator-project-selection)
- [`fact-comparator-pinout`](#fact-comparator-pinout)

## Cross-component rules

Rules that span several parts at once and are published in full on the integration page. Each rule's verdict below is that rule's own — it is a statement about the cross-component question, not about this part — and the exact wording of what the rule refuses to conclude is published with the rule itself.

No cross-component rule names this record.

## Sources

Every document cited above, with its identification, when it was retrieved, and what kind of authority it carries. Sources that could not be retrieved are listed too, with their unavailability stated, so a gap in the evidence is visible rather than absent.

### LM393B, LM2903B, LM193, LM293, LM393 and LM2903 Dual Comparators datasheet (Rev. AH)

<EvidenceAnchor id="src-comparator-datasheet" />

**Source ID:** `src-comparator-datasheet` · **Authority:** MANUFACTURER\_PRIMARY

| Field | Recorded value |
| --- | --- |
| Document number | SLCS005AH |
| Revision | AH |
| Document date | April 2025 |
| Retrieved | 2026-09-28 |
| Printed page | 3 |

**Locator:** Pin configuration/function table

**Availability:** AVAILABLE

**Document URL:** [https://www.ti.com/lit/ds/symlink/lm393b.pdf](https://www.ti.com/lit/ds/symlink/lm393b.pdf)

### OSC-ES-1 parts shortlist

<EvidenceAnchor id="src-comparator-shortlist" />

**Source ID:** `src-comparator-shortlist` · **Authority:** PROJECT\_GENERATOR

| Field | Recorded value |
| --- | --- |
| Document number | OSC-ES-1 |
| Revision | base SHA b185391d30ec38293bc6c5e8b798a282b98baa25 |
| Document date | 2026-09-28 |
| Retrieved | 2026-09-28 |
| Printed page | not paginated |

**Locator:** JSON row parts\[id=comparator], fields manufacturer/mpn/package/lcsc/sourcing

**Availability:** AVAILABLE

**Document URL:** [https://github.com/Takazudo/zudo-osc-hole-field/blob/base/osc-hole-field/design/standard/parts-shortlist.json](https://github.com/Takazudo/zudo-osc-hole-field/blob/base/osc-hole-field/design/standard/parts-shortlist.json)

## Legend

What the recorded terms on this page mean, in ordinary words. The exact terms above are the ones that count; these descriptions explain them and never replace them.

### Verdict

| Recorded term | What it means |
| --- | --- |
| `NEEDS BENCH` | Cannot be settled from documents. It needs measurement on real hardware before it can be relied on. |
| `NOT APPLICABLE` | The parameter does not apply to this part as it is used here. |
| `PASS - primary-source confirmed` | Confirmed against the manufacturer's own document for this exact part. |
| `UNSOURCED` | No accepted source backs this value yet. Treat it as a claim, not a fact. |

### Provenance

| Recorded term | What it means |
| --- | --- |
| `PRIMARY-SPEC` | Taken from the manufacturer's own specification document. |
| `PROJECT-CHOICE` | A decision made by this project. No vendor asserts it. |

### Fact class

| Recorded term | What it means |
| --- | --- |
| `GUARANTEED_ELECTRICAL` | A parameter the manufacturer guarantees over the stated conditions, usually with minimum, typical and maximum values. |
| `PROJECT_STATE` | A value this project recorded about how the part is used here — a chosen operating point, a net assignment, or a derived figure. Not a manufacturer specification. |

### Coverage status

| Recorded term | What it means |
| --- | --- |
| `COVERED` | Every question this domain asks is answered by the facts listed against it. |
| `OPEN` | Unresolved. Open means the question has not been answered, not that the part is unsafe — the reason states what is missing. |

### Source availability

| Recorded term | What it means |
| --- | --- |
| `AVAILABLE` | The document was retrieved and is on record. |

### Source authority

| Recorded term | What it means |
| --- | --- |
| `MANUFACTURER_PRIMARY` | The manufacturer's own document for this exact part. |
| `PROJECT_GENERATOR` | A document this project generated, such as a schematic or netlist export. |

### Identity state

| Recorded term | What it means |
| --- | --- |
| `VERIFIED` | The exact orderable part has been confirmed against a source. |

### Source state

| Recorded term | What it means |
| --- | --- |
| `AVAILABLE` | At least one document backing this line was retrieved. |

### Unit

| Recorded term | What it means |
| --- | --- |
| `NONE` | The value is not a physical quantity, so it carries no unit. Recorded as \`NONE\`. |

## Raw agent resource

This page is generated from a stored evidence bundle and does not restate it. The bundle is the source of truth: where the two ever disagree, the bundle is right and this page is stale.

[Open the owning bundle](/docs/claude-skills/component-ti-lm393bidr/) `component-ti-lm393bidr`
