Takazudo/zudo-osc-hole-field/doc/src/content/docs/components/records/flipflop/index.mdx

---
# GENERATED by @takazudo/zudo-circuit-doc — do not edit; run `zudo-circuit-doc generate`
title: "SN74HC74DR"
description: "envelope state — Texas Instruments — no placement published — rec-flipflop"
sidebar_position: 18
---

<EvidenceAnchor id="rec-flipflop" />

Generated from the component evidence records — edit the records, not this page.

Everything below is projected from this project's stored component evidence. Values keep the exact wording, conditions, units and verdicts they were recorded with — nothing here is re-typed, corrected, or combined into an overall judgement about the part.

This record in the catalog: [SN74HC74DR](/docs/components/catalog/#rec-flipflop)

## Identity

| Field | Recorded value |
| --- | --- |
| Record ID | `rec-flipflop` |
| Record kind | standalone |
| Manufacturer part number | `SN74HC74DR` |
| Manufacturer | Texas Instruments |
| Function | envelope state |
| LCSC ID | Not assigned; order by exact manufacturer part number |
| Package | `SOIC-14` |
| Inventory line | `line-flipflop` |
| Owner skill | `component-ti-sn74hc74dr` |

**Fit:** Fitted

**Identity state:** VERIFIED

**Source state:** AVAILABLE

**Coverage:** 3 open of 6 published

## Documents and package

<EvidenceAnchor id="component-references-heading" />

<ComponentReferences descriptor="7b2276657273696f6e223a312c22646f63756d656e74223a7b226c6162656c223a2244617461736865657420504446222c227469746c65223a22534e783448433734204475616c20442d5479706520506f7369746976652d456467652d54726967676572656420466c69702d466c6f7073205769746820436c65617220616e64205072657365742064617461736865657420285265762e204629222c22617574686f72697479223a224d414e5546414354555245525f5052494d415259222c22617661696c6162696c697479223a22415641494c41424c45222c2275726c223a2268747470733a2f2f7777772e74692e636f6d2f6c69742f64732f73796d6c696e6b2f736e3734686337342e706466227d2c22666f6f747072696e74223a7b226e616d65223a22534f49432d31345f332e3978382e376d6d5f50312e32376d6d222c22617373657455726c223a222f6173736574732f636f6d706f6e656e742d70726576696577732f666f6f747072696e74732f534f49432d31345f332e3978382e376d6d5f50312e32376d6d2e737667227d2c226d6f64656c44657363726970746f72223a2237623232373636353732373336393666366532323361333132633232373036313633366236313637363534393634323233613232353334663439343332643331333435663333326533393738333832653337366436643566353033313265333233373664366432323263323237303631363336623631363736353463363136323635366332323361323235333466343934333264333133343566333332653339373833383265333736643664356635303331326533323337366436643232326332323664366636343635366335353732366332323361323232663631373337333635373437333266363336663664373036663665363536653734326437303732363537363639363537373733326636643666363436353663373332663439343335663533346634393433326433313334356633333265333937383338326533373265373737323663323232633232366636363636373336353734323233613762323237383232336133303263323237393232336133303263323237613232336133303764326332323732366637343631373436393666366532323361376232323738323233613330326332323739323233613330326332323761323233613330376432633232373336333631366336353232336137623232373832323361333132633232373932323361333132633232376132323361333137643764227d" />

**Selected document:** [Datasheet PDF](https://www.ti.com/lit/ds/symlink/sn74hc74.pdf) — SNx4HC74 Dual D-Type Positive-Edge-Triggered Flip-Flops With Clear and Preset datasheet (Rev. F)

**Selected source ID:** `src-flipflop-datasheet`

**Authority:** MANUFACTURER\_PRIMARY

**Availability:** AVAILABLE

**Package footprint:** `SOIC-14_3.9x8.7mm_P1.27mm`

This geometry represents a shared footprint package and may not exactly match the manufacturer part.

## Placements

No board placement is published for this record.

## Coverage

Coverage is stated one domain at a time and is never rolled up. A domain marked open is a question that has not been answered; it is not a finding that the part is unsuitable. A record with no open domains has not thereby been declared safe.

### exact orderable identity

<EvidenceAnchor id="cov-flipflop-exact-orderable-identity" />

**Coverage ID:** `cov-flipflop-exact-orderable-identity` · **Status:** COVERED

**Reason:** Manufacturer primary bytes identify the exact shortlist MPN/package; supplier stock remains separately open.

**Facts in this domain:**

- [`fact-flipflop-orderable-identity`](#fact-flipflop-orderable-identity)

### pinout

<EvidenceAnchor id="cov-flipflop-pinout" />

**Coverage ID:** `cov-flipflop-pinout` · **Status:** COVERED

**Reason:** The retained manufacturer document provides the listed pin-function table; no project nets are assigned.

**Facts in this domain:**

- [`fact-flipflop-pinout`](#fact-flipflop-pinout)

### electrical limits

<EvidenceAnchor id="cov-flipflop-electrical-limits" />

**Coverage ID:** `cov-flipflop-electrical-limits` · **Status:** OPEN

**Reason:** UNSOURCED full application closure: selected table rows do not establish all actual-supply, load, startup and partial-power behavior.

**Facts in this domain:**

- [`fact-flipflop-electrical-limits`](#fact-flipflop-electrical-limits)

**Blocked by:** these facts must be resolved before the domain can close. Each is listed in full under Facts.

- [`fact-flipflop-electrical-limits`](#fact-flipflop-electrical-limits)

### manufacturer product description

<EvidenceAnchor id="cov-flipflop-manufacturer-product-description" />

**Coverage ID:** `cov-flipflop-manufacturer-product-description` · **Status:** COVERED

**Reason:** The retained manufacturer document identifies the named product and its documented role/description; this is not application qualification.

**Facts in this domain:**

- [`fact-flipflop-product-function`](#fact-flipflop-product-function)

### mechanical fit

<EvidenceAnchor id="cov-flipflop-mechanical-fit" />

**Coverage ID:** `cov-flipflop-mechanical-fit` · **Status:** OPEN

**Reason:** The local family envelope and generic footprint are provisional; physical board fit and land-pattern suitability are not validated.

**Facts in this domain:**

- [`fact-flipflop-mechanical-fit`](#fact-flipflop-mechanical-fit)

**Blocked by:** these facts must be resolved before the domain can close. Each is listed in full under Facts.

- [`fact-flipflop-mechanical-fit`](#fact-flipflop-mechanical-fit)

### procurement

<EvidenceAnchor id="cov-flipflop-procurement" />

**Coverage ID:** `cov-flipflop-procurement` · **Status:** OPEN

**Reason:** Supplier stock, lead time, consignment and assembly allocation remain unverified as of the dated shortlist.

**Facts in this domain:**

- [`fact-flipflop-procurement-status`](#fact-flipflop-procurement-status)

**Blocked by:** these facts must be resolved before the domain can close. Each is listed in full under Facts.

- [`fact-flipflop-procurement-status`](#fact-flipflop-procurement-status)

## Facts

Each fact keeps its value, its unit, the conditions it holds under, where it came from and how far it has been confirmed as separate fields, because they are separate claims. A value without its conditions is not the same fact, and a verdict is about the evidence for the value, not about the part.

### RECOMMENDED\_OPERATION

The range the manufacturer intends the part to be used in. Always narrower than the absolute maximum.

<EvidenceFact>
  <EvidenceAnchor id="fact-flipflop-temperature" />

  **Fact:** `fact-flipflop-temperature`

  **Value:** `maximum`=85; `minimum`=-40 · **Unit:** `degC`

  **Conditions:** SN74HC74DR grade; not the SN54 range.

  **Verdict:** PASS - primary-source confirmed · **Provenance:** PRIMARY-SPEC

  **Evidence:** [src-flipflop-datasheet: printed p4 section6.3](#src-flipflop-datasheet)
</EvidenceFact>

<EvidenceFact>
  <EvidenceAnchor id="fact-flipflop-input-transition45" />

  **Fact:** `fact-flipflop-input-transition45`

  **Value:** 500 · **Unit:** `ns`

  **Conditions:** Maximum input rise/fall transition at VCC4.5V. The table prints unit ns; this is not an HC14 Schmitt-input constraint.

  **Verdict:** PASS - primary-source confirmed · **Provenance:** PRIMARY-SPEC

  **Evidence:** [src-flipflop-datasheet: printed p4 section6.3](#src-flipflop-datasheet)
</EvidenceFact>

### GUARANTEED\_ELECTRICAL

A parameter the manufacturer guarantees over the stated conditions, usually with minimum, typical and maximum values.

<EvidenceFact>
  <EvidenceAnchor id="fact-flipflop-electrical-limits" />

  **Fact:** `fact-flipflop-electrical-limits`

  **Value:** Selected source-conditioned logic rows are retained; whole project supply/load/partial-power applicability remains unestablished. · **Unit:** `NONE`

  **Conditions:** Source table points are not silently promoted into complete permit qualification.

  **Verdict:** UNSOURCED · **Provenance:** UNVERIFIED

  **Evidence:** [src-flipflop-datasheet: selected electrical and timing tables; application closure remains open](#src-flipflop-datasheet)
</EvidenceFact>

<EvidenceFact>
  <EvidenceAnchor id="fact-flipflop-quiescent-table-max" />

  **Fact:** `fact-flipflop-quiescent-table-max`

  **Value:** 0.00004 · **Unit:** `A`

  **Conditions:** SN74, TA=-40..85C, VCC=6V, VI=VCC or 0, IO=0. No maximum loaded-output or switching-current claim at the candidate 5V supply.

  **Verdict:** PASS - primary-source confirmed · **Provenance:** PRIMARY-SPEC

  **Evidence:** [src-flipflop-datasheet: printed p5 section6.5 ICC row, SN74 column](#src-flipflop-datasheet)
</EvidenceFact>

### TRANSIENT

Behaviour during a short event — startup, a switching edge, a fault or a surge.

<EvidenceFact>
  <EvidenceAnchor id="fact-flipflop-clear-pulse45" />

  **Fact:** `fact-flipflop-clear-pulse45`

  **Value:** 25 · **Unit:** `ns`

  **Conditions:** Minimum PRE/CLR low pulse at VCC4.5V, TA -40..85C.

  **Verdict:** PASS - primary-source confirmed · **Provenance:** PRIMARY-SPEC

  **Evidence:** [src-flipflop-datasheet: printed p6 section6.7 -74 timing requirements](#src-flipflop-datasheet)
</EvidenceFact>

<EvidenceFact>
  <EvidenceAnchor id="fact-flipflop-clock-pulse45" />

  **Fact:** `fact-flipflop-clock-pulse45`

  **Value:** 20 · **Unit:** `ns`

  **Conditions:** Minimum CLK high or low pulse at VCC4.5V, TA -40..85C.

  **Verdict:** PASS - primary-source confirmed · **Provenance:** PRIMARY-SPEC

  **Evidence:** [src-flipflop-datasheet: printed p6 section6.7 -74 timing requirements](#src-flipflop-datasheet)
</EvidenceFact>

<EvidenceFact>
  <EvidenceAnchor id="fact-flipflop-clear-setup45" />

  **Fact:** `fact-flipflop-clear-setup45`

  **Value:** 6 · **Unit:** `ns`

  **Conditions:** Minimum PRE/CLR inactive interval before CLK rising at VCC4.5V, TA -40..85C. No independent removal-time row is inferred.

  **Verdict:** PASS - primary-source confirmed · **Provenance:** PRIMARY-SPEC

  **Evidence:** [src-flipflop-datasheet: printed p6 section6.7 -74 timing requirements](#src-flipflop-datasheet)
</EvidenceFact>

<EvidenceFact>
  <EvidenceAnchor id="fact-flipflop-reset-delay45" />

  **Fact:** `fact-flipflop-reset-delay45`

  **Value:** 58 · **Unit:** `ns`

  **Conditions:** Maximum PRE/CLR to Q at VCC4.5V, TA -40..85C, CL50pF, input transitions \<6ns.

  **Verdict:** PASS - primary-source confirmed · **Provenance:** PRIMARY-SPEC

  **Evidence:** [src-flipflop-datasheet: printed p7 section6.9 and p9 section7](#src-flipflop-datasheet)
</EvidenceFact>

<EvidenceFact>
  <EvidenceAnchor id="fact-flipflop-clock-delay45" />

  **Fact:** `fact-flipflop-clock-delay45`

  **Value:** 44 · **Unit:** `ns`

  **Conditions:** Maximum CLK to Q at VCC4.5V, TA -40..85C, CL50pF, input transitions \<6ns.

  **Verdict:** PASS - primary-source confirmed · **Provenance:** PRIMARY-SPEC

  **Evidence:** [src-flipflop-datasheet: printed p7 section6.9 and p9 section7](#src-flipflop-datasheet)
</EvidenceFact>

### PROJECT\_STATE

A value this project recorded about how the part is used here — a chosen operating point, a net assignment, or a derived figure. Not a manufacturer specification.

<EvidenceFact>
  <EvidenceAnchor id="fact-flipflop-manufacturer" />

  **Fact:** `fact-flipflop-manufacturer`

  **Value:** Texas Instruments · **Unit:** `NONE`

  **Conditions:** Manufacturer of the project-selected exact shortlist identity.

  **Verdict:** PASS - primary-source confirmed · **Provenance:** PRIMARY-SPEC

  **Evidence:** [src-flipflop-datasheet: title block or OSC-ES-1 row parts\[id=flipflop\].manufacturer](#src-flipflop-datasheet)
</EvidenceFact>

<EvidenceFact>
  <EvidenceAnchor id="fact-flipflop-project-selection" />

  **Fact:** `fact-flipflop-project-selection`

  **Value:** `lcsc`=not listed in the shortlist; `manufacturer`=Texas Instruments; `mpn`=SN74HC74DR; `package`=SOIC-14; `roles`=envelope state; `source_status`=UNVERIFIED · **Unit:** `NONE`

  **Conditions:** OSC-ES-1 dated proposal row; exact source status and availability statements are not supplier allocation.

  **Verdict:** NOT APPLICABLE · **Provenance:** PROJECT-CHOICE

  **Evidence:** [src-flipflop-shortlist: JSON row parts\[id=flipflop\]](#src-flipflop-shortlist)
</EvidenceFact>

<EvidenceFact>
  <EvidenceAnchor id="fact-flipflop-orderable-identity" />

  **Fact:** `fact-flipflop-orderable-identity`

  **Value:** `manufacturer`=Texas Instruments; `mpn`=SN74HC74DR; `package`=SOIC-14 · **Unit:** `NONE`

  **Conditions:** Exact complete orderable identifier in the selected package; does not establish supplier stock.

  **Verdict:** PASS - primary-source confirmed · **Provenance:** PRIMARY-SPEC

  **Evidence:** [Section/table audit: src-flipflop-datasheet: package/orderable addendum names exact MPN](#src-flipflop-datasheet)
</EvidenceFact>

<EvidenceFact>
  <EvidenceAnchor id="fact-flipflop-pinout" />

  **Fact:** `fact-flipflop-pinout`

  **Value:** pin 1 1CLR active low -> pad 1; pin 2 1D data -> pad 2; pin 3 1CLK rising edge -> pad 3; pin 4 1PRE active low -> pad 4; pin 5 1Q -> pad 5; pin 6 1Q inverted -> pad 6; pin 7 GND -> pad 7; pin 8 2Q inverted -> pad 8; pin 9 2Q -> pad 9; pin 10 2PRE active low -> pad 10; pin 11 2CLK rising edge -> pad 11; pin 12 2D data -> pad 12; pin 13 2CLR active low -> pad 13; pin 14 VCC -> pad 14 · **Unit:** `NONE`

  **Conditions:** No schematic or placement/net binding is claimed. Manufacturer pin functions are source-backed only when a retained primary document names the product family.

  **Verdict:** PASS - primary-source confirmed · **Provenance:** PRIMARY-SPEC

  **Evidence:** [src-flipflop-datasheet: Pin configuration/function table](#src-flipflop-datasheet)
</EvidenceFact>

<EvidenceFact>
  <EvidenceAnchor id="fact-flipflop-product-function" />

  **Fact:** `fact-flipflop-product-function`

  **Value:** Manufacturer source identifies SN74HC74DR as the shortlisted envelope state device; this is not project suitability. · **Unit:** `NONE`

  **Conditions:** Product family description only; no project application or electrical guarantee implied.

  **Verdict:** PASS - primary-source confirmed · **Provenance:** PRIMARY-SPEC

  **Evidence:** [src-flipflop-datasheet: document title block and product description](#src-flipflop-datasheet)
</EvidenceFact>

<EvidenceFact>
  <EvidenceAnchor id="fact-flipflop-procurement-status" />

  **Fact:** `fact-flipflop-procurement-status`

  **Value:** UNVERIFIED · **Unit:** `NONE`

  **Conditions:** Time-stamped OSC-ES-1 state on 2026-09-28; current stock, lead time, consignment, and JLC assembly are not established.

  **Verdict:** UNSOURCED · **Provenance:** PROJECT-CHOICE

  **Evidence:** [src-flipflop-shortlist: JSON row parts\[id=flipflop\].sourcing.status/jlcpcb\_assembly](#src-flipflop-shortlist)
</EvidenceFact>

<EvidenceFact>
  <EvidenceAnchor id="fact-flipflop-mechanical-fit" />

  **Fact:** `fact-flipflop-mechanical-fit`

  **Value:** Provisional package-family envelope only; board/land-pattern fit has not been physically checked. · **Unit:** `NONE`

  **Conditions:** Selected footprint family and display envelope do not establish exact-part placement or solderability.

  **Verdict:** NEEDS BENCH · **Provenance:** PROJECT-CHOICE

  **Evidence:** [Section/table audit: src-flipflop-shortlist: parts\[id=flipflop\].package; CAD receipt is provisional family geometry](#src-flipflop-shortlist)
</EvidenceFact>

## Pin maps

The mapping between schematic pins and PCB pads, or physical terminals for an external part, as recorded. A record may carry more than one map when the same part is documented in more than one context.

### pinmap-flipflop

<EvidenceAnchor id="pinmap-flipflop" />

- **Symbol:** `SN74HC74DR`
- **Footprint:** `SOIC-14_3.9x8.7mm_P1.27mm`
- **Pins:** 14

<EvidenceDetails label="pin-assignments">
  <EvidenceTable label="pin-assignments">
    | Symbol pin | Name               | Footprint pad | Function         |
    | ---------- | ------------------ | ------------- | ---------------- |
    | `1`        | `1CLR active low`  | `1`           | 1CLR active low  |
    | `2`        | `1D data`          | `2`           | 1D data          |
    | `3`        | `1CLK rising edge` | `3`           | 1CLK rising edge |
    | `4`        | `1PRE active low`  | `4`           | 1PRE active low  |
    | `5`        | `1Q`               | `5`           | 1Q               |
    | `6`        | `1Q inverted`      | `6`           | 1Q inverted      |
    | `7`        | `GND`              | `7`           | GND              |
    | `8`        | `2Q inverted`      | `8`           | 2Q inverted      |
    | `9`        | `2Q`               | `9`           | 2Q               |
    | `10`       | `2PRE active low`  | `10`          | 2PRE active low  |
    | `11`       | `2CLK rising edge` | `11`          | 2CLK rising edge |
    | `12`       | `2D data`          | `12`          | 2D data          |
    | `13`       | `2CLR active low`  | `13`          | 2CLR active low  |
    | `14`       | `VCC`              | `14`          | VCC              |
  </EvidenceTable>
</EvidenceDetails>

## Interactions

Behaviour that is not a property of this part alone. Each interaction names the records it spans, the conditions it holds under, and how far it has been confirmed. An interaction that spans several parts appears on every one of their pages, under the same identifier, because it is equally a fact about each.

### int-flipflop-project-role

<EvidenceAnchor id="int-flipflop-project-role" />

- **Records involved:** `rec-flipflop` (this record)
- **Conditions:** Project role from OSC-ES-1; schematic nets, board placements, pin assignment and circuit behavior remain unbound.
- **Verdict:** NEEDS BENCH

**Facts this rests on:**

- [`fact-flipflop-project-selection`](#fact-flipflop-project-selection)
- [`fact-flipflop-pinout`](#fact-flipflop-pinout)

## Cross-component rules

Rules that span several parts at once and are published in full on the integration page. Each rule's verdict below is that rule's own — it is a statement about the cross-component question, not about this part — and the exact wording of what the rule refuses to conclude is published with the rule itself.

- [`monitor-permit-startup`](/docs/components/integration/#monitor-permit-startup) — unselected monitor/reference/latch startup and power loss — **rule verdict:** UNSOURCED

[All cross-component rules](/docs/components/integration/)

## Sources

Every document cited above, with its identification, when it was retrieved, and what kind of authority it carries. Sources that could not be retrieved are listed too, with their unavailability stated, so a gap in the evidence is visible rather than absent.

### SNx4HC74 Dual D-Type Positive-Edge-Triggered Flip-Flops With Clear and Preset datasheet (Rev. F)

<EvidenceAnchor id="src-flipflop-datasheet" />

**Source ID:** `src-flipflop-datasheet` · **Authority:** MANUFACTURER\_PRIMARY

| Field | Recorded value |
| --- | --- |
| Document number | SCLS094F |
| Revision | F |
| Document date | June 2021 |
| Retrieved | 2026-09-28 |
| Printed page | 3 |

**Locator:** Pin configuration/function table

**Availability:** AVAILABLE

**Document URL:** [https://www.ti.com/lit/ds/symlink/sn74hc74.pdf](https://www.ti.com/lit/ds/symlink/sn74hc74.pdf)

### OSC-ES-1 parts shortlist

<EvidenceAnchor id="src-flipflop-shortlist" />

**Source ID:** `src-flipflop-shortlist` · **Authority:** PROJECT\_GENERATOR

| Field | Recorded value |
| --- | --- |
| Document number | OSC-ES-1 |
| Revision | base SHA b185391d30ec38293bc6c5e8b798a282b98baa25 |
| Document date | 2026-09-28 |
| Retrieved | 2026-09-28 |
| Printed page | not paginated |

**Locator:** JSON row parts\[id=flipflop], fields manufacturer/mpn/package/lcsc/sourcing

**Availability:** AVAILABLE

**Document URL:** [https://github.com/Takazudo/zudo-osc-hole-field/blob/base/osc-hole-field/design/standard/parts-shortlist.json](https://github.com/Takazudo/zudo-osc-hole-field/blob/base/osc-hole-field/design/standard/parts-shortlist.json)

## Legend

What the recorded terms on this page mean, in ordinary words. The exact terms above are the ones that count; these descriptions explain them and never replace them.

### Verdict

| Recorded term | What it means |
| --- | --- |
| `NEEDS BENCH` | Cannot be settled from documents. It needs measurement on real hardware before it can be relied on. |
| `NOT APPLICABLE` | The parameter does not apply to this part as it is used here. |
| `PASS - primary-source confirmed` | Confirmed against the manufacturer's own document for this exact part. |
| `UNSOURCED` | No accepted source backs this value yet. Treat it as a claim, not a fact. |

### Provenance

| Recorded term | What it means |
| --- | --- |
| `PRIMARY-SPEC` | Taken from the manufacturer's own specification document. |
| `PROJECT-CHOICE` | A decision made by this project. No vendor asserts it. |
| `UNVERIFIED` | Recorded, but not yet backed by an accepted source. |

### Fact class

| Recorded term | What it means |
| --- | --- |
| `GUARANTEED_ELECTRICAL` | A parameter the manufacturer guarantees over the stated conditions, usually with minimum, typical and maximum values. |
| `PROJECT_STATE` | A value this project recorded about how the part is used here — a chosen operating point, a net assignment, or a derived figure. Not a manufacturer specification. |
| `RECOMMENDED_OPERATION` | The range the manufacturer intends the part to be used in. Always narrower than the absolute maximum. |
| `TRANSIENT` | Behaviour during a short event — startup, a switching edge, a fault or a surge. |

### Coverage status

| Recorded term | What it means |
| --- | --- |
| `COVERED` | Every question this domain asks is answered by the facts listed against it. |
| `OPEN` | Unresolved. Open means the question has not been answered, not that the part is unsafe — the reason states what is missing. |

### Source availability

| Recorded term | What it means |
| --- | --- |
| `AVAILABLE` | The document was retrieved and is on record. |

### Source authority

| Recorded term | What it means |
| --- | --- |
| `MANUFACTURER_PRIMARY` | The manufacturer's own document for this exact part. |
| `PROJECT_GENERATOR` | A document this project generated, such as a schematic or netlist export. |

### Identity state

| Recorded term | What it means |
| --- | --- |
| `VERIFIED` | The exact orderable part has been confirmed against a source. |

### Source state

| Recorded term | What it means |
| --- | --- |
| `AVAILABLE` | At least one document backing this line was retrieved. |

### Unit

| Recorded term | What it means |
| --- | --- |
| `NONE` | The value is not a physical quantity, so it carries no unit. Recorded as \`NONE\`. |

## Raw agent resource

This page is generated from a stored evidence bundle and does not restate it. The bundle is the source of truth: where the two ever disagree, the bundle is right and this page is stale.

[Open the owning bundle](/docs/claude-skills/component-ti-sn74hc74dr/) `component-ti-sn74hc74dr`
