Takazudo/zudo-osc-hole-field/doc/src/content/docs/components/records/npn/index.mdx

---
# GENERATED by @takazudo/zudo-circuit-doc — do not edit; run `zudo-circuit-doc generate`
title: "MMBT3904,215"
description: "LED current sink; general transistor — Nexperia — no placement published — rec-npn"
sidebar_position: 29
---

<EvidenceAnchor id="rec-npn" />

Generated from the component evidence records — edit the records, not this page.

Everything below is projected from this project's stored component evidence. Values keep the exact wording, conditions, units and verdicts they were recorded with — nothing here is re-typed, corrected, or combined into an overall judgement about the part.

This record in the catalog: [MMBT3904,215](/docs/components/catalog/#rec-npn)

## Identity

| Field | Recorded value |
| --- | --- |
| Record ID | `rec-npn` |
| Record kind | standalone |
| Manufacturer part number | `MMBT3904,215` |
| Manufacturer | Nexperia |
| Function | LED current sink; general transistor |
| LCSC ID | Not assigned; order by exact manufacturer part number |
| Package | `SOT-23` |
| Inventory line | `line-npn` |
| Also known as | `LED current sink`, `general transistor` |
| Owner skill | `component-nexperia-mmbt3904-215` |

**Fit:** Fitted

**Identity state:** VERIFIED

**Source state:** AVAILABLE

**Coverage:** 3 open of 6 published

## Documents and package

<EvidenceAnchor id="component-references-heading" />

<ComponentReferences descriptor="7b2276657273696f6e223a312c22646f63756d656e74223a7b226c6162656c223a2244617461736865657420504446222c227469746c65223a22343020562c20323030206d41204e504e20737769746368696e67207472616e736973746f72222c22617574686f72697479223a224d414e5546414354555245525f5052494d415259222c22617661696c6162696c697479223a22415641494c41424c45222c2275726c223a2268747470733a2f2f6173736574732e6e657870657269612e636f6d2f646f63756d656e74732f646174612d73686565742f4d4d4254333930342e706466227d2c22666f6f747072696e74223a7b226e616d65223a22534f542d3233222c22617373657455726c223a222f6173736574732f636f6d706f6e656e742d70726576696577732f666f6f747072696e74732f534f542d32332e737667227d2c226d6f64656c44657363726970746f72223a22376232323736363537323733363936663665323233613331326332323730363136333662363136373635343936343232336132323533346635343264333233333232326332323730363136333662363136373635346336313632363536633232336132323533346635343264333233333232326332323664366636343635366335353732366332323361323232663631373337333635373437333266363336663664373036663665363536653734326437303732363537363639363537373733326636643666363436353663373332663439343335663533346635343264333233333265373737323663323232633232366636363636373336353734323233613762323237383232336133303263323237393232336133303263323237613232336133303764326332323732366637343631373436393666366532323361376232323738323233613330326332323739323233613330326332323761323233613330376432633232373336333631366336353232336137623232373832323361333132633232373932323361333132633232376132323361333137643764227d" />

**Selected document:** [Datasheet PDF](https://assets.nexperia.com/documents/data-sheet/MMBT3904.pdf) — 40 V, 200 mA NPN switching transistor

**Selected source ID:** `src-npn-datasheet`

**Authority:** MANUFACTURER\_PRIMARY

**Availability:** AVAILABLE

**Package footprint:** `SOT-23`

This geometry represents a shared footprint package and may not exactly match the manufacturer part.

## Placements

No board placement is published for this record.

## Coverage

Coverage is stated one domain at a time and is never rolled up. A domain marked open is a question that has not been answered; it is not a finding that the part is unsuitable. A record with no open domains has not thereby been declared safe.

### exact orderable identity

<EvidenceAnchor id="cov-npn-exact-orderable-identity" />

**Coverage ID:** `cov-npn-exact-orderable-identity` · **Status:** OPEN

**Reason:** The current exact MPN is a project-selected proposal but its full manufacturer orderable identity/package suffix is not confirmed by retained exact-part bytes.

**Facts in this domain:**

- [`fact-npn-orderable-identity`](#fact-npn-orderable-identity)

**Blocked by:** these facts must be resolved before the domain can close. Each is listed in full under Facts.

- [`fact-npn-orderable-identity`](#fact-npn-orderable-identity)

### pinout

<EvidenceAnchor id="cov-npn-pinout" />

**Coverage ID:** `cov-npn-pinout` · **Status:** COVERED

**Reason:** The retained manufacturer document provides the listed pin-function table; no project nets are assigned.

**Facts in this domain:**

- [`fact-npn-pinout`](#fact-npn-pinout)

### electrical limits

<EvidenceAnchor id="cov-npn-electrical-limits" />

**Coverage ID:** `cov-npn-electrical-limits` · **Status:** COVERED

**Reason:** Retained source supports the specific listed product-family limits; conditions remain attached to each fact.

**Facts in this domain:**

- [`fact-npn-collector-emitter-voltage`](#fact-npn-collector-emitter-voltage)

### manufacturer product description

<EvidenceAnchor id="cov-npn-manufacturer-product-description" />

**Coverage ID:** `cov-npn-manufacturer-product-description` · **Status:** COVERED

**Reason:** The retained manufacturer document identifies the named product and its documented role/description; this is not application qualification.

**Facts in this domain:**

- [`fact-npn-product-function`](#fact-npn-product-function)

### mechanical fit

<EvidenceAnchor id="cov-npn-mechanical-fit" />

**Coverage ID:** `cov-npn-mechanical-fit` · **Status:** OPEN

**Reason:** The local family envelope and generic footprint are provisional; physical board fit and land-pattern suitability are not validated.

**Facts in this domain:**

- [`fact-npn-mechanical-fit`](#fact-npn-mechanical-fit)

**Blocked by:** these facts must be resolved before the domain can close. Each is listed in full under Facts.

- [`fact-npn-mechanical-fit`](#fact-npn-mechanical-fit)

### procurement

<EvidenceAnchor id="cov-npn-procurement" />

**Coverage ID:** `cov-npn-procurement` · **Status:** OPEN

**Reason:** Supplier stock, lead time, consignment and assembly allocation remain unverified as of the dated shortlist.

**Facts in this domain:**

- [`fact-npn-procurement-status`](#fact-npn-procurement-status)

**Blocked by:** these facts must be resolved before the domain can close. Each is listed in full under Facts.

- [`fact-npn-procurement-status`](#fact-npn-procurement-status)

## Facts

Each fact keeps its value, its unit, the conditions it holds under, where it came from and how far it has been confirmed as separate fields, because they are separate claims. A value without its conditions is not the same fact, and a verdict is about the evidence for the value, not about the part.
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
