Takazudo/zudo-osc-hole-field/project/osc-hole-field/VALIDATION-HANDOFF.md

# Validation — zudo-osc-hole-field R21 handoff

## Executed in this session

| Check | Actual result | What it proves |
|---|---|---|
| Workbench structural checks | 45 passed | Grid counts, cell coverage, part references, format/links and existing browser result |
| Existing grid/AR logic tests | 15 passed | Ideal behavior and 2D mappings |
| New SLEW model tests | 18 passed | Exact first-order analytical updates, independent targets, continuity, endpoints and invalid input handling |
| Browser checks | 43/43 passed | Flat controls, source IDs, S&H targets, added controls, unchanged hardware scale, WebGL, stationary-frame stability and mobile overflow |
| Handoff checks | 66 passed before the final hash manifest; one additional hash check runs when the manifest exists | Actual source preservation, payload identities, 45 authored MDX pages, local links and source receipt honesty |
| Importer safety tests | 10 passed | Dry run, collision rejection, symlink guard, idempotence, authored text preservation and no runtime/evidence overwrite |
| Full payload import test | Passed on a synthetic host | Copy, append-links, allowlist update and idempotence for the actual complete payload |
| PDF proof | 318 × 298 mm within 0.02 mm | Actual generated page dimensions, not hole/fit qualification |

Browser: 144.0.7559.96. Headed Chromium under Xvfb with SwiftShader. The exact self-contained HTML bytes were loaded with `set_content`; direct `file://` navigation is blocked by this environment. No external runtime assets were requested. A stable stationary frame is not a promise about every GPU/browser.

The panel, enlarged SLEW controls, primary RC diagram and print proof were rendered and visually inspected. The 3D model remains simplified package/case geometry and proposed mounting planes, not certified manufacturer CAD. The new SLEW board/pot positions are included.

## Not run / not established

- Official `create-zudo-circuit-doc` execution, dependency installation and native documentation build. This environment has Node 22.16.0, below the reviewed minimum 22.18.0; direct source/package downloads also encountered DNS failure. Repo content was read through GitHub, and exact commands are supplied for local execution.
- Native runtime evidence validation. No fabricated v1 owner bundles or declared PASS facts were inserted. Candidates remain authored research and an explicit promotion queue.
- New original TI/FH/Bourns datasheet bytes or exact new model downloads. Primary parsed web text was reviewed; Bourns dimensions were visually checked by PDF screenshot. TI PDF screenshots failed. New exact data must be reacquired and hash-locked locally. No URL or extracted page is mislabeled as an original PDF receipt.
- ngspice execution: `slew-ideal.cir` is a starting behavioral test deck. The executed JS/Python tests use ideal RC mathematics, not real op-amp/LF398 models.
- Native KiCad load/ERC/DRC, complete schematic, component pin-to-pad qualification, routing, manufacturing output, 3D interference/tolerance/structural checks, sample hardware, thermal tests or electrical bench results.
- Supply programming/NVM confirmation, actual JLC order availability, quotations, procurement, factory acceptance or shipment.

## Interpretation

A completed feature grid is not a completed electrical design. The SLEW range is a proposal. The LF398 drift/offset caveat is a real design task, not fixed by glide. The exact jack/nut and component-board mounting stack must be solved before routing. A separate rear PCB does not by itself prove a shallow physical assembly.

`SHA256SUMS.json` describes the delivered bytes. Intentional local edits and regenerated screenshots/reports will require a new review snapshot; do not force old hashes or weaken validation to hide changes.
