Takazudo/zudo-osc-hole-field/circuit/routing/issue189/focused-tests.txt

.....................................  refill pass 1: 1 open edges
  refill pass 2: 1 open edges
  refill pass 3: 1 open edges
  refill pass 4: 1 open edges
  refill pass 5: 1 open edges
  refill pass 6: 1 open edges
.  refill pass 1: 1 open edges
  refill pass 2: 1 open edges
  refill pass 3: 1 open edges
.  refill pass 1: 23 open edges
  refill pass 2: 29 open edges
  refill pass 3: 23 open edges
  refill pass 4: 29 open edges
  refill pass 5: 23 open edges
  refill pass 6: 29 open edges
.  refill pass 1: 29 open edges
  refill pass 2: 23 open edges
  refill pass 3: 23 open edges
  refill pass 4: 29 open edges
  refill pass 5: 29 open edges
  refill pass 6: 29 open edges
..........shards-test: 2 -> 1 open edges
promoted boards/osc-jack-left/osc-jack-left.kicad_pcb
shards-test: 2 -> 1 open edges
shards-test: 2 -> 1 open edges
.shards-recovery: 2 -> 0 open edges
promoted boards/osc-jack-left/osc-jack-left.kicad_pcb
.......................................................................
----------------------------------------------------------------------
Ran 122 tests in 1.458s

OK
