Takazudo/zudo-osc-hole-field/circuit/routing/issue189/jr130-rb4615-via-branch/targeted-tests.txt

..........shards-complete: 3 -> 1 open edges
promoted boards/osc-jack-left/osc-jack-left.kicad_pcb
shards-complete: 3 -> 1 open edges
shards-complete: 3 -> 1 open edges
shards-complete: 3 -> 1 open edges
shards-complete: 3 -> 1 open edges
.shards-test: 2 -> 1 open edges
promoted boards/osc-jack-left/osc-jack-left.kicad_pcb
shards-test: 2 -> 1 open edges
shards-test: 2 -> 1 open edges
.shards-recovery: 2 -> 0 open edges
promoted boards/osc-jack-left/osc-jack-left.kicad_pcb
.merge attempt 1: reverting 1 nets with failing copper
shards-retention: 2 -> 2 open edges
merge attempt 1: reverting 1 nets with failing copper
shards-retention-again: 2 -> 2 open edges
.............................
----------------------------------------------------------------------
Ran 42 tests in 0.885s

OK
