Takazudo/zudo-osc-hole-field/doc/src/content/docs/verification/osc-pcb-jack.mdx

---
title: "JL/JR PCB routed draft"
description: "Six-layer jack halves after locality re-placement: native routing status and remaining qualification."
---

**Routed draft in progress — unvalidated, not reviewed as hardware, not a fabrication release. [Issue #38 remains OPEN](https://github.com/Takazudo/zudo-osc-hole-field/issues/38).** Electrical and physical qualification are **NOT RUN**. No fabrication or order files were generated.

## Owner decision 2026-10-03: six layers with locality re-placement

A cut-line bound (`scripts/pcbgen/cut_capacity.py`) showed that the four-layer halves could not carry their signal nets with intact ground and power planes. About 400 nets had to cross single jack-pin columns whose front/back capacity was only 0.80–0.86 of that demand. The owner chose both remedies: six copper layers and locality re-placement of the free surface-mount packages. Panel hardware, LEDs and headers do not move.

- **Placement:** `scripts/checks/jack_locality.py` replaces the connectivity-blind first-fit J placement. Each free package is pulled toward the fixed jacks, LEDs and headers on its signal nets and toward its own module's fixed hardware, then legalized onto the nearest free courtyard cells. IC/bypass clusters are placed first and keep their supply-pad alignment (worst 2.8875 mm against the 3 mm proposal). After legalization, packages with the same footprint trade slots (side and rotation travel with the slot, so every swap stays legal) to cut span-weighted wire length, with a quadratic penalty above 60 mm. This cuts the estimated wire length from 25.5 to 18.1 m on JL (nets longer than 60 mm 79 → 21) and from 25.1 to 18.0 m on JR (53 → 13). The output is byte-stable across hash seeds.
- **Stack:** F.Cu, In2.Cu, In3.Cu and B.Cu carry signals; In1.Cu is a continuous AGND plane; In3.Cu also carries the −12 V fill; In4.Cu is a continuous +12 V plane. +5 V is routed as 0.4 mm tracks. Signals on In3.Cu are accepted only if the −12 V fill stays connected, and native checks reject any batch that splits it.
- **Neck-down at IC pin rows:** `scripts/pcbgen/neckdown_areas.py` draws a rule area (nothing disallowed) over every IC whose pins carried an open signal net on the routed drafts, covering its pads plus 2 mm, from `design/partition/neckdown-areas.json`. Each half's `.kicad_dru` lets Default-class signal copper inside these areas use 0.15 mm track width and 0.15 mm signal-to-signal clearance (0.2 mm / 0.2 mm elsewhere). This is common practice and within standard six-layer fabrication capability; it gives the router room to escape the quad op-amp pin rows. Rails and AGND keep their 0.25 mm net-class clearance, and the grid router applies the same rule per region.
- **Evidence chain:** `scripts/checks/jack_locality.py` proves the partition changed only in jack package faces, jack bypass distances and the jack layer stack, and chains onto the earlier connector-locality transition. Superseded four-layer stage reports were removed; git history keeps them.

## Current half-board status

| Native check | JL / `osc-jack-left` | JR / `osc-jack-right` |
| --- | --- | --- |
| Status | ROUTED DRAFT IN PROGRESS | ROUTED DRAFT IN PROGRESS |
| Native open edges (DRC, settled zone refill) | **117** | **130** |
| Remaining signal edges | 103 | 107 |
| Remaining rail / ground edges | +12V 0, +5V 0, -12V 0, AGND 14 | +12V 0, +5V 0, -12V 0, AGND 23 |
| DRC errors / schematic parity | 0 / 0 | 0 / 0 |
| Track segments / vias | 30564 / 2861 | 48445 / 3129 |
| Native warnings | hole to hole 2, silk edge clearance 8, silk over copper 199, silk overlap 199, text height 43, track dangling 4, via dangling 22 | hole to hole 24, silk edge clearance 13, silk over copper 199, silk overlap 199, text height 59, track dangling 3, via dangling 23 |

Routing uses `scripts/pcbgen/route_jack_grid.py`: terminal via arrays, ±12 V plane fanouts, rail links, then a negotiated-congestion (PathFinder) pass over every signal net on a 0.05 mm grid (region stages re-run on a 0.035 mm grid inside the neck-down areas), rip-up-and-reroute batches for what it leaves open, with AGND stitching vias where new copper cuts a surface pour. Each stage is applied to a disposable copy, checked with native DRC, schematic parity and zone refill, and kept only when the native open-edge count falls. Rip-up-and-reroute re-offers still-open islands with 4, 8, 12 and then 20 victim nets per probe, and a stranded island joins whichever island of its net is cheapest to reach, not only the largest. Stage receipts are in `boards/<board-id>/reports/grid-routing/`; `reports/ratsnest.json` holds the native per-net topology after a single zone refill; the open-edge figures above come from DRC with refilled zones, which can be higher. Silkscreen/text warnings remain [#44](https://github.com/Takazudo/zudo-osc-hole-field/issues/44).

The images below predate the #189 routing transactions; refreshed renders remain part of final integration. The table and native receipts describe the current copper.

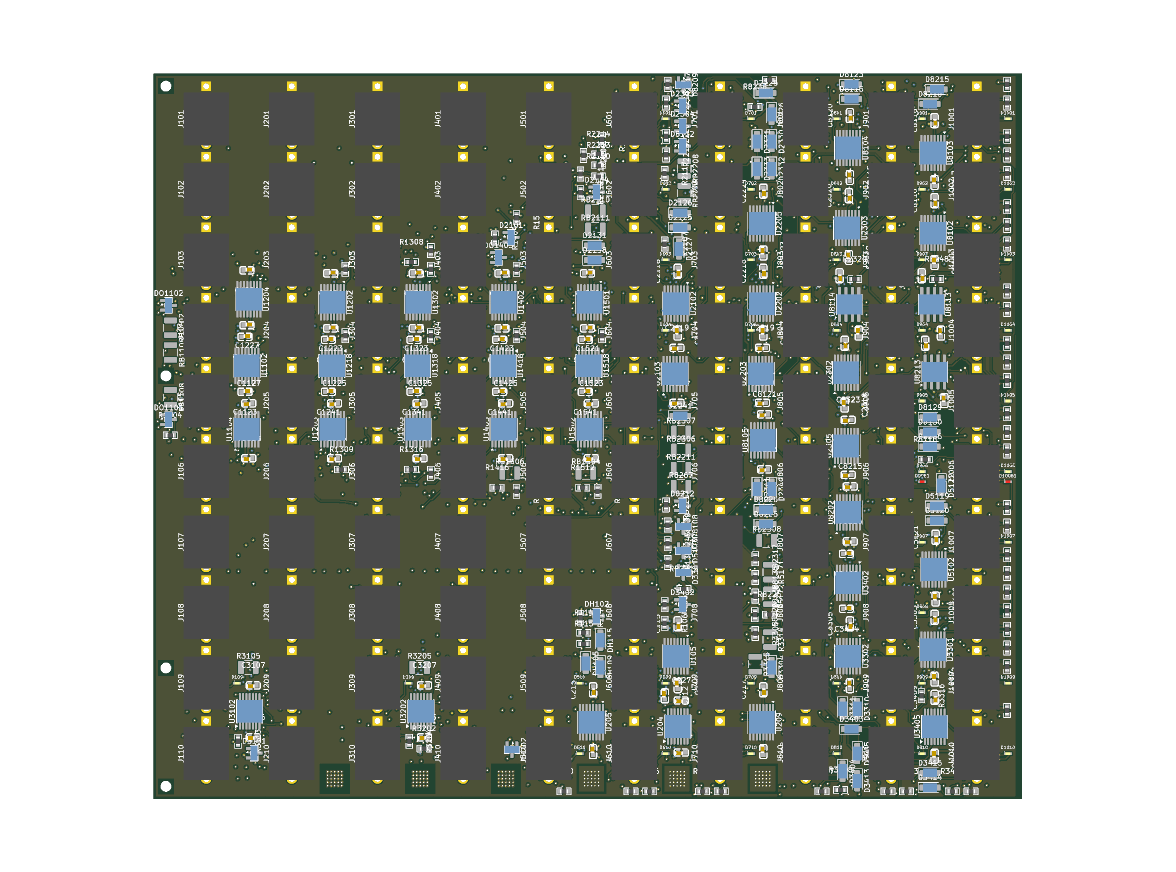
[picture p24: doc/public/assets/osc-hole-field/osc-jack-left-top.png]
JL top: unvalidated routed draft


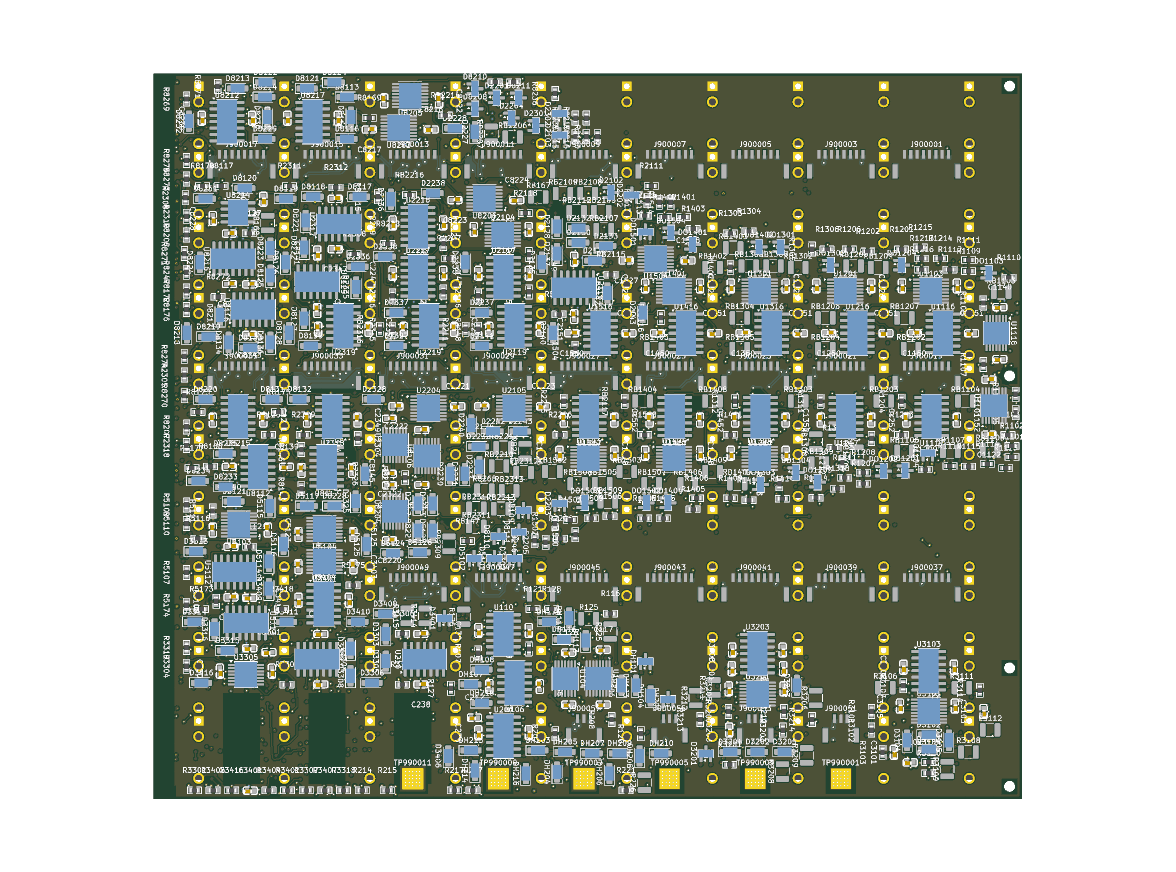
[picture p25: doc/public/assets/osc-hole-field/osc-jack-left-bottom.png]
JL bottom: unvalidated routed draft


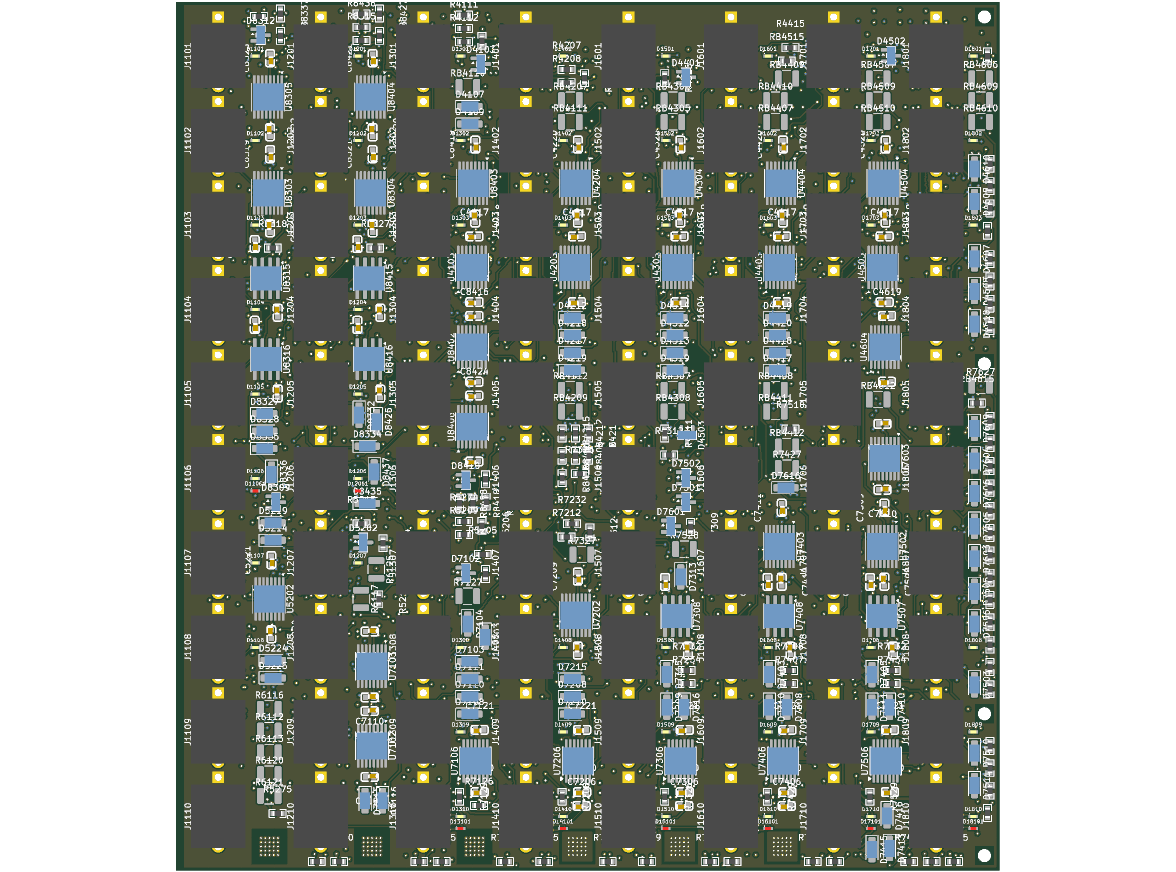
[picture p26: doc/public/assets/osc-hole-field/osc-jack-right-top.png]
JR top: unvalidated routed draft


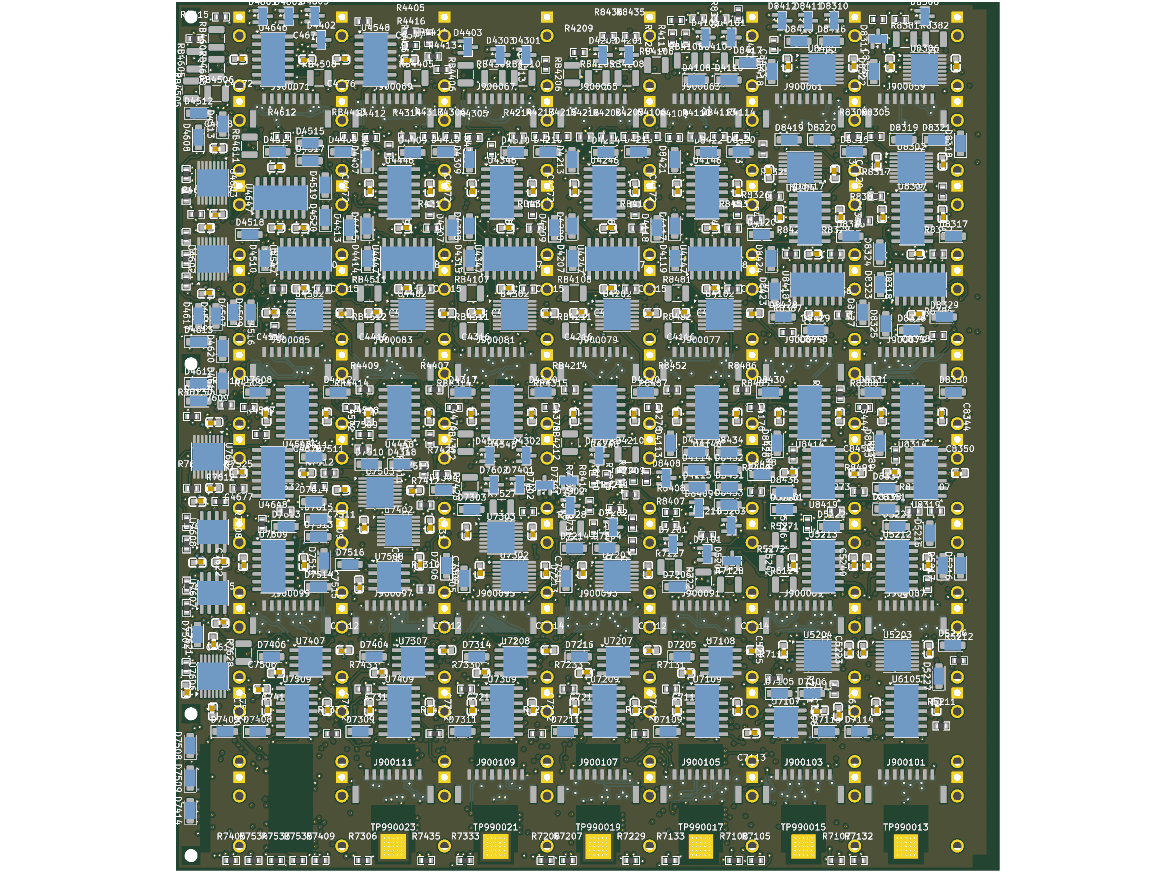
[picture p27: doc/public/assets/osc-hole-field/osc-jack-right-bottom.png]
JR bottom: unvalidated routed draft


## Qualification remains NOT RUN

The earlier field-solver ground/current extraction is parked and is not a routing gate. Rail and return resistance, hot distribution drop, GH contact current, the 5×5 filled/capped via-in-pad terminal arrays (#65 process), protection (#59), source/inlet (#57), selector (#55), LED (#64) and installed fit (#65) all remain unqualified. Continue [#38](https://github.com/Takazudo/zudo-osc-hole-field/issues/38) for the remaining open edges.

## Historical rejected single-J experiment

**Historical #38 evidence, superseded by the #66 JL/JR source partition.** Counts, paths and routing results below describe the rejected single board, not either current half.

**Draft layout — autorouting attempted, not reviewed as hardware, not a fabrication release.** No fabrication order files have been generated.

| Item | Historical rejected result |
| --- | --- |
| Board | `osc-jack`, panel frame x4–314, y20–164 mm (310 × 144 mm) |
| Stack | Four copper layers, 1.6 mm, proposed 2 oz; F.Cu faces the panel at proposed z = −10 mm |
| Population | 2,091 assigned master packages: 180 fixed jacks, 102 fixed compact LEDs, and 1,809 free local circuit packages; 56 rear JST GH headers and six factory load-side lands; eight Ø2.2 mm M2 support holes |
| Placement | All 2,153 netlisted footprints retain the #35 per-reference origin, KiCad angle, and F/B face; eight board-only supports retain their source coordinates. KiCad courtyard placement passed. |
| Rule DRC / schematic parity | Zero rule errors and zero schematic-parity issues before routing. Warnings concern silkscreen/text and isolated copper. |
| Routing | **UNROUTED DRAFT.** The guarded 180-second fanout and 900-second no-fanout attempts both timed out before writing an SES. No router copper was imported; track and via counts remain zero. This does not meet the issue's bounded incomplete-routing allowance. |
| Routed / unrouted | Zero new router tracks or vias; 5,611 complete native KiCad ratsnest edges remain. The exact number of unrouted *nets* is not available from the capped CLI JSON. It lists only 499 items and three sampled net names; `boards/osc-jack/reports/ratsnest.json` gives 1,362 multi-pad *candidate* net names, which are not a claim that each remains open. |
| AGND branch plus K neck | **NOT RUN** — layout extraction and K routing are needed to verify the combined ≤0.5 mΩ condition, including vias. Hot physical measurement remains #65. |

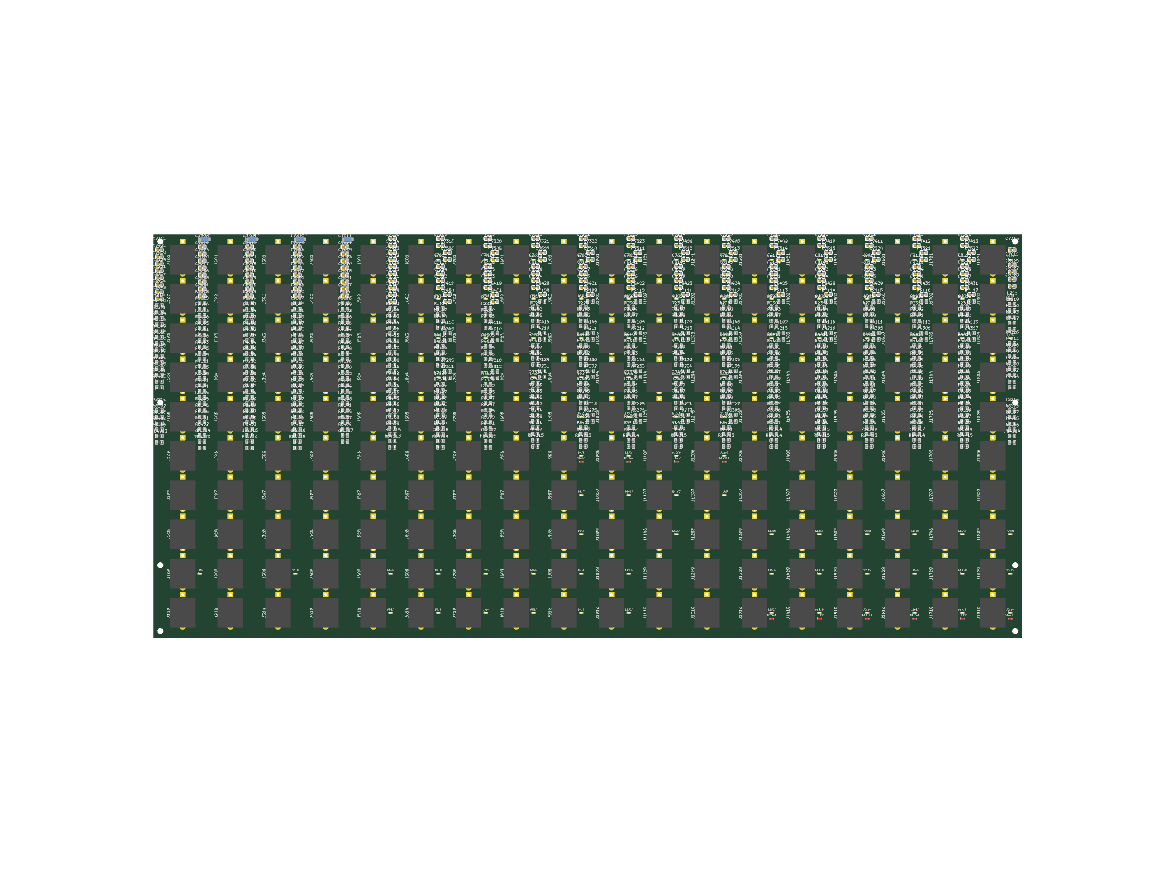
[picture p28: doc/public/assets/osc-hole-field/osc-jack-top.png]
Top render of the unvalidated osc-jack PCB draft


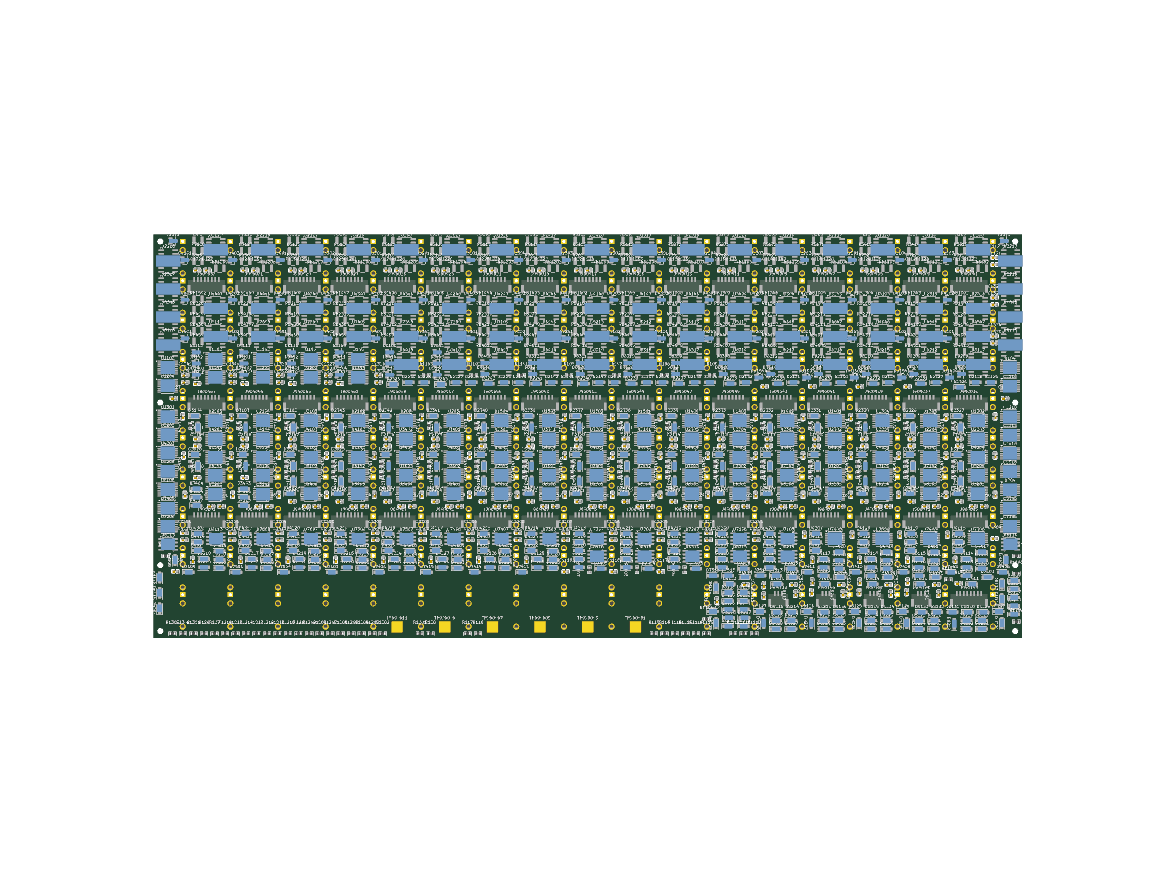
[picture p29: doc/public/assets/osc-hole-field/osc-jack-bottom.png]
Bottom render of the unvalidated osc-jack PCB draft


The [partition source](../architecture/osc-board-stack.mdx) preserves the gross B-face #59 output and precision-sense protection rectangle x120–310/y143–161 (3,420 mm²). The `design/partition/partition.json` subtraction receipt records 2,029.2 mm² occupied by 30 fixed jack courtyard intersections, leaving 1,390.8 mm² after jack exclusions. Three separate 5 × 3 mm bulk slots consume another 45 mm² of that area, leaving at most 1,345.8 mm² for output/sense protection. The bulk slots were moved within the proposed rectangle to clear current source courtyards. Their exact capacitor identities and protection circuit dimensions remain **OPEN #59**; no fit is inferred from the remaining area.

`boards/osc-jack/reports/replication-feasibility.json` compares 22 repeated J module pairs against the exact source face and footprint centres. None has a complete single translation, so whole-module route replay would require a source placement revision. `routing-attempt-1.json` records the first timeout; `routing.json` records the second. Both left 5,611 native ratsnest edges and no copper. A revised J partition or placement/routing strategy is required before #38 can close. The current `boards/osc-jack/reports/drc.json` and top/bottom PNGs are the native KiCad 10.0.6 evidence.

Physical seated fit, jack nut/shoulder clearance, supports, looms, factory load wires, hot resistance, and enclosure depth: **NOT RUN #65**. Selector coupon **NOT RUN #55**; physical source/inlet **NOT RUN #57**; LED optical/hot qualification **NOT RUN #64**. The 82 output and 16 precision-sense protection obligations remain **OPEN #59**. The 0.35 mm compact-LED/jack nominal courtyard gap is drawing-derived and does not establish assembled fit.

## Issue #189 implementation checkpoint

[Draft PR #190](https://github.com/Takazudo/zudo-osc-hole-field/pull/190) reproduces
and fixes removed-via drill exclusions and soft probes through fixed pads. On
identical saved native inputs, the old router left JL at 140; the correction
reached 139 with no pad-membership split or new warning. The replay was independently
checked and adopted in `e0efa315`; a subsequent bounded rip-up stage remained at
139 without changing copper. JR stayed at 162 in both variants. Three diagnosed
local JR probes also produced no copper and are retained as negative evidence.

JL retains 32,667 physical copper objects unchanged, replaces 78 and adds 117.
Eleven legacy duplicated copper UUIDs are preserved; the original benchmark's
UUID-map counts undercounted physical objects by eleven. The separate retention
audit corrects that metric. All 1,099 footprints, outline/setup and 128 zone
definitions are unchanged. Existing hole-to-hole warnings remain recorded, not
waived as cosmetic. Exact native results, warning identities, hashes and next
interventions are in `circuit/routing/issue189/`. #189 and hardware qualification
remain open.

### Targeted branch-repair pilots (2026-10-09)

Read-only native local repairs retained cut fragments as reconnection obligations.
JL went 139→141 after its three-segment cut, then returned to 139; no gain was
adopted. JR went 162→168 after its 23-segment cut, then 163; one victim pad group
and dangling-copper warnings regressed, so that proposal was rejected. Independent
checks agreed with both experimental counts. That experiment left canonical JL/JR at 139/162; the later supply replay below reduces JL to 138.

The JR target and failed victim were blocked by the −12 V fill guard. A subsequent
source proposal is being evaluated as a joint signal/supply transaction: native
supply restoration and the original baseline's membership/warning gates remain
mandatory. Its intermediate signal-only proposal is not acceptable copper. The
ordinary routing fill guard, dimensions, fixed geometry and final native gates
remain unchanged. Exact negative results and replay hashes are retained under
`circuit/routing/issue189/`.

### Isolated supply replay (2026-10-09)

[Native replay 37881515385](https://github.com/Takazudo/zudo-osc-hole-field/actions/runs/37881515385)
adopted one 0.65 mm -12V segment, reducing JL 139→138. All 32,784 existing physical
copper objects remain unchanged; zero removals. Native errors/parity are 0/0,
no warning identities or original pad groups regress, and independent reload
agrees. The replay and receipt are `shards-issue189-rail-leaf*` in JL's routing
reports; adopted board SHA is
`f9eff29fc92c4533ab518ebdc6dbc2ead2a53e5d0f03f2eb5891814608bfa65e`.

The larger coupled signal/rail proposal also reported 138 but split an original
AGND group and was rejected. Only the independently checked isolated segment
was adopted. JR's 13-path additive candidate was rejected for original -12V
membership change; its lower raster count is not accepted progress.

### Bounded corridor replay (2026-10-09)

[Native replay 37885619978](https://github.com/Takazudo/zudo-osc-hole-field/actions/runs/37885619978)
adopted JL 138→137. The physical soft-probe corridor selected seven blockers on
three signal nets; native topology reconstructed every retained boundary fragment.
The transaction adds 157 objects, removes 7, and retains 32,778 original copper
objects. DRC/parity remain 0/0, all original pad groups remain connected, no new
warning identities appear, and an independent reload agrees. Source/replay hashes
and the acceptance receipt are in `shards-issue189-corridor*` routing reports.

[JR native replay 37886650433](https://github.com/Takazudo/zudo-osc-hole-field/actions/runs/37886650433)
adopted the seven-signal proposal plus explicit supply restoration, reducing
162→155. All 50,311 original copper objects remain unchanged; 401 objects were
added and none removed. DRC/parity are 0/0, the 520 existing reported warnings
have no new identities, all original pad groups remain connected, and independent
reload agrees. Supply/return counts remain +12V 0, −12V 5 and AGND 29.
The replay and receipt are `shards-issue189-return-restored*`; board SHA is
`cf8cabf2e115e294a7a67253eae290ecd02a57419b5996a54e8755fcf79196cf`.

JL/JR/core completion remains open under #189. The follow-on corridor pilots
are experiments, not adopted copper or hardware qualification.

### Isolated pair of corridors (2026-10-09)

[Native replay 37888369139](https://github.com/Takazudo/zudo-osc-hole-field/actions/runs/37888369139)
adopted JL 137→135. U3404.10 and U2119.3 plus their complete victim repairs were
isolated from a rejected six-corridor pilot. The accepted pair retains 32,910
original objects, removes 25 selected blockers and adds 214 objects. DRC/parity
are 0/0; all original pad groups and warning identities are preserved, and an
independent reload agrees. Board SHA is
`3d40f1db27f350ce063bf601cab2eeb9f6394b47da9930fca21b6bc0258d2352`.
The larger pilot's two split victim groups and four dangling warnings remain
recorded as a rejection; its unaccepted copper is not part of this board.

### Bounded ground and signal repairs (PR #195)

[JL replay 37896098143](https://github.com/Takazudo/zudo-osc-hole-field/actions/runs/37896098143)
adopted 135→134 after repairing R1301.2 and explicitly correcting the signal
junctions and dangling tails. It retains 33,103 original copper objects, removes
21 diagnosed objects and adds 28. Native errors/parity are 0/0, with 477 existing
warnings, no new warning identities or original pad-group splits, and independent
fresh-copy agreement.

[JR ground replay 37894363972](https://github.com/Takazudo/zudo-osc-hole-field/actions/runs/37894363972)
adopted 155→154 with 24 additions and no removals. The subsequent
[U7509 replay 37896805484](https://github.com/Takazudo/zudo-osc-hole-field/actions/runs/37896805484)
adopted 154→153, preserving all 24 ground additions. Across both steps, 50,699
original objects remain unchanged, 13 are replaced and 57 are added. Native
errors/parity are 0/0, with 520 existing warnings and no new warning identities or
original pad-group splits; independent fresh-copy verification agrees.

The next two-ground pilot, run 37897562881, was rejected at 135 edges because two
signal groups split and four dangling warnings appeared. Its copper is not adopted.
The exact replay, hashes, retention checks and continuing pilot state are recorded
in `circuit/routing/issue189/checkpoint.md`. Complete connectivity and hardware
qualification remain open; the earlier renders have not been refreshed.

### All jack supply edges connected (PR #197)

[JL canonical replay 37903090712](https://github.com/Takazudo/zudo-osc-hole-field/actions/runs/37903090712)
adopted 134→127, and
[JR canonical replay 37903349098](https://github.com/Takazudo/zudo-osc-hole-field/actions/runs/37903349098)
adopted 153→148. Both now have zero +12V, −12V and +5V native open edges.
AGND remains at 22/28 and signal edges at 105/120, so routing is incomplete.

Each transaction adds ten 0.25 mm outer-layer supply segments, with no vias or
removals. All 33,131 JL and 50,756 JR pre-existing copper objects remain unchanged.
Native errors/parity are 0/0; existing 477/520 warnings retain their identities,
no original pad groups split, and independent fresh-copy connectivity agrees.
The canonical board hashes match the independently checked pilot boards.

The finer raster resolves these short escapes without changing electrical rules.
A separate regression prevents supply and ground paths from inheriting signal
neck-down dimensions. Earlier undersized raster proposals were never adopted.
No routing result establishes current capacity, powered behavior or manufacturing
qualification. Exact receipts and further signal/ground work remain under #189.

[Native replay 37905262670](https://github.com/Takazudo/zudo-osc-hole-field/actions/runs/37905262670)
then adopted JR148→146 with 33 additive signal objects and no removed copper.
All 50,766 prior objects, including ten new supply segments, remain unchanged.
Native DRC/parity are 0/0, original pad groups and warning identities are preserved,
and independent fresh-copy connectivity agrees. JL D2326 was then adopted127→126 in run37906767213 with six segments and two
vias added,zero removed objects,all33,141prior objects retained,and the same native
preservation/fresh-copy gates passing.

The first bounded fine-raster replay, [37907617523](https://github.com/Takazudo/zudo-osc-hole-field/actions/runs/37907617523),
then adopted JR146→145. It retained all50,799prior copper objects and added20segments
and2vias,with no removals,new warning identities,pad-group splits,DRC or parity
errors;independent fresh-copy connectivity agrees.

Native run 37916090766 on 2026-10-09 adopted **JR145→143**. Excluding the D7504
transaction that split R7505.2/R7530.2 ground connectivity left two independent
signal transactions: 87 segments and 6 vias, with zero removed objects. All 50,821
prior copper objects remain identical. Native errors/parity are 0/0, with 520
unchanged warnings, no new warning identities or split pad groups, and independent
fresh-copy agreement. The rejected three-net 145→144 result is retained as negative
evidence; it was never adopted. Exact replay and retention receipts are in
`circuit/routing/issue189/jr-two-without-d7504` and the board's grid-routing reports.

Native run 37918072226 adopted **JL126→125** using an additive U106 outer-layer
path: 69 segments and 2 vias, with all 33,149 prior copper objects unchanged.
Native errors/parity are 0/0, with 477 unchanged warnings, no new warning identities
or split pad groups, and independent fresh-copy agreement. The earlier three-cut
U106 pilot was rejected because both victims remained split; none of that removed
copper is part of this accepted transaction. Exact hashes and retention evidence
are in `circuit/routing/issue189/jl-u106-outer` and the native grid-routing receipts.

Native run [37920931258](https://github.com/Takazudo/zudo-osc-hole-field/actions/runs/37920931258)
adopted **JR143→141** with 50 additive objects, preserving all 50,914 prior objects.
Native run [37929676316](https://github.com/Takazudo/zudo-osc-hole-field/actions/runs/37929676316)
then adopted **JR141→140** with 26 F.Cu segments and no vias or removals. This
D7208 alternative avoids the earlier proposal that split the −12 V fill.
All 50,964 prior objects remain identical. Both accepted transactions have zero
native DRC/parity errors, 520 unchanged warnings, no new warning identities or
split pad groups, and independent fresh-copy agreement. Exact hashes, replay and
retention evidence are in `circuit/routing/issue189/jr-two-after-protected` and
`circuit/routing/issue189/jr-d7208-no-via`. Further D7504 proposals were rejected
for AGND splits and are not included in the current copper.

Native run [37932246042](https://github.com/Takazudo/zudo-osc-hole-field/actions/runs/37932246042)
adopted **JL125→124** with a full-width C8143.2 ground fanout: one segment and
one via, zero removals, all 33,220 prior copper objects identical. Native
DRC/parity are 0/0, with 477 unchanged warnings, no split original pad groups or
new warning identities, and independent fresh-copy agreement. The pad/net,
outline, keepout and layer records are unchanged. Exact artifact and retention
receipts are in `circuit/routing/issue189/jl-c8143-fanout`.

Native run `37933235474` then accepted **JR140→139** by isolating the 27 B.Cu
R8487 segments from the rejected two-net candidate. All 50,990 prior copper
objects remained identical. Run `37934138351` accepted **JL124→121** with 17
segments and three vias joining R2209, RB2217 and the U3402 ground cluster; all
33,222 prior objects remained identical. Both have zero native DRC/parity errors,
unchanged warning identities, no split original pad groups and matching fresh
connectivity. These are partial routing improvements, not fabrication approval.

Run `37936737740` subsequently accepted **JR139→137** with seven full-width
ground segments and two vias for R8407 and the C8329/U8303/C8318 group. All
51,017 prior copper objects, 3,655 pads, four outline edges, 154 keepouts and
six layers are unchanged. Native DRC/parity remain zero, all 520 warnings are
unchanged, original pad groups do not split, and the fresh check agrees.

Runs `37947934139` and `37947938555` accepted **JL121→120 / JR137→136**.
These coupled ground repairs replace one reviewed JL signal segment and two JR
segments, reserve explicit ground links, restore the original signal groups, and
connect every retained endpoint exposed by the cuts. The preceding candidates
were rejected for dangling retained tracks; the accepted proposals add short
endpoint links without extra vias or cuts. JL adds 53 objects and retains all
33,241 uncut objects; JR adds 39 and retains all 51,024 uncut objects. Both have
zero native DRC/parity errors, unchanged 477/520 warnings, no new warning identities
or split original pad groups, and fresh native agreement. Every pad, outline edge,
rule area and copper layer is unchanged; project/rule files are byte-identical.
Exact pilot/adoption hashes and full retention proofs are in
`circuit/routing/issue189/jl-u2204-endpoints` and `jr-u8303-endpoints`.

Run `37960073108` accepted **JL120→119** after the U1518 joint pilot passed.
The fixed transaction reserves an explicit ground connection and restores both
native-cut signal components with 58 segments, no vias and four reviewed cuts.
All 33,290 uncut objects remain identical; every pad, outline edge, rule area,
layer and project/rule file is unchanged. Native DRC/parity are zero, all 477
warnings are unchanged, original pad groups do not split, and fresh connectivity
agrees. Published board and replay hashes exactly match the eligible pilot.
Evidence is in `circuit/routing/issue189/jl-u1518-joint`.

Run `37960834229` accepted **JR136→135** after the R4207 joint pilot passed.
The fixed transaction adds 85 segments and one via with four reviewed cuts,
reserving ground before restoring the bare-pad signal component. All 51,059
uncut objects remain identical. Native DRC/parity are zero, all 520 warnings
are unchanged, original pad groups remain intact, and fresh connectivity agrees.
Every physical and project/rule invariant is unchanged; published board and
replay hashes exactly match the eligible pilot. The first adoption attempt
failed before routing at a workflow allowlist and is not native evidence; its
regression and correction are retained. Evidence is in
`circuit/routing/issue189/jr-r4207-joint`.

Run `37967123290` accepted **JR135→134** after the C7413 endpoint pilot passed.
The replay adds 37 segments with five reviewed cuts and retains all 51,140 uncut
objects. It has zero native DRC/parity errors, unchanged 520 warning identities,
no original pad-group splits and fresh native agreement. Published board and
replay hashes exactly match the eligible pilot; pad, outline, keepout, layer,
project and electrical-rule invariants remain unchanged. Complete evidence is
in `circuit/routing/issue189/jr-c7413-endpoints/`. This remains a routed draft.

### Accepted continuation through 2026-10-10

[Run 37978945582](https://github.com/Takazudo/zudo-osc-hole-field/actions/runs/37978945582)
accepted **JL119→118** with the R8276 joint repair: 75 added segments, two reviewed
cuts, and all 33,346 uncut copper objects retained. Native DRC/parity are 0/0,
original connected pad groups remain intact, warning identities are unchanged,
and fresh-copy connectivity agrees. That accepted revision has 33,421 copper objects
and SHA256 `a01df89dcab3d4fab8eb0ae80195b2825d2d47adc517cd73452d9b9aa6ea079a`.

[PR #230](https://github.com/Takazudo/zudo-osc-hole-field/pull/230) subsequently
accepted **JL118→117** with the R8127 joint repair. It retains all 33,418 uncut
objects, removes exactly one reviewed via and two attached segments, and adds
six segments and one via. All 1,111 nonrouting objects are unchanged. Native
KiCad 10.0.6 settled and independent fresh checks agree at 117, with DRC/parity
0/0, no original group split and all 477 warning findings preserved. Complete
audits cover two hole identities on each side, seven new-copper fixtures and
20 paired-zone fixtures. The current JL board has 33,425 copper objects and
SHA256 `e984c0a01156b5f282f0c849077c61572df30ee0c70dfe6c9db94fbfcfe52107`.
Its full native run is
[38038883190](https://github.com/Takazudo/zudo-osc-hole-field/actions/runs/38038883190);
all five exact bot CI checks passed before merge.

[PR #220](https://github.com/Takazudo/zudo-osc-hole-field/pull/220) accepted
**JR134→133**, adding 74 segments and five vias while retaining all 51,177 old
objects. [PR #223](https://github.com/Takazudo/zudo-osc-hole-field/pull/223)
then accepted **JR133→131**, adding 143 segments and three vias while retaining
all 51,256 old objects. Neither transaction cuts copper or moves components.
Both pass complete native warning inventories, DRC/parity, original pad-group
preservation and independent fresh-copy checks. That accepted revision has 51,402
copper objects and SHA256 `7bb70ac47e12c8bb2e2362d78f7602bdf99c2a69214c68aebeef273b0ce11965`.

[PR #224](https://github.com/Takazudo/zudo-osc-hole-field/pull/224) subsequently
accepted **JR131→130**, adding 167 segments and five vias without cuts or moves.
All 51,402 old copper objects and 1,080 nonrouting objects remain unchanged.
Settled and independent fresh checks agree at 130, with native DRC/parity 0/0,
no original group split and all 520 complete warning findings preserved. Full
audits cover 24 hole identities on each side, 172 new-copper fixtures and
50 paired-zone fixtures. The current JR board has 51,574 copper objects and
SHA256 `e06b7471ddc8f5c8c498c5eb5bf8655cc6de539e92826a5701cf1de06356e136`.
Its full native run is
[38032373766](https://github.com/Takazudo/zudo-osc-hole-field/actions/runs/38032373766);
all five exact bot CI checks passed before merge.

The U8202 and RB4615 joint proposals are tracked separately and are not
included in the accepted table. Earlier JL U8215
pilots were rejected because they split existing J900035 ground groups and
raised native open edges to 120; no rejected copper was adopted. Exact artifact
digests, retained-copper proofs and continuation commands are in the
[immutable routing checkpoint](https://github.com/Takazudo/zudo-osc-hole-field/blob/892749dbdd53cfbab2d0876424fc4aecf1fa4311/circuit/routing/issue189/current-native-checkpoint.md).
