Takazudo/zudo-osc-hole-field/doc/src/content/docs/verification/osc-pcb-core.mdx

---
title: "Core PCB routed draft"
description: "Six-layer core board after locality placement and rail routing: native routing status and remaining qualification."
---

**Routed draft in progress. It is unvalidated, has not been reviewed as hardware, and is not a fabrication release. [Issue #43 remains OPEN](https://github.com/Takazudo/zudo-osc-hole-field/issues/43).** Electrical and physical qualification are **NOT RUN**. No fabrication or order files were generated.

## Placement: module-spread locality

`scripts/checks/partition35_floorplan.py` places the 3,385 free core packages with `scripts/checks/jack_locality.py`. The core has no panel hardware, so the core GH header pins anchor each signal net.

The first header-anchored placement crowded about 1,300 envelope/offset packages into one corner and scattered modules: 751 nets spanned 80 mm or more. Negotiated routing then stalled at about 2,500 of 2,727 nets in conflict. The current placement (v3) adds three steps:

- **Module home discs.** Each module gets an area-proportional disc around its header home. `scripts/checks/core_locality.py:spread_module_homes` pushes the discs apart inside the outline and the notch. Packages are then legalized one module at a time, largest first.
- **Core-only spacing.** A 0.6 mm courtyard gap and a 0.5 mm keep-clear ring around each IC.
- **Swap pass.** A same-footprint swap pass penalizes nets longer than 60 mm, with candidates within 25 mm of each package's net median.

Through-hole packages block both faces. IC + bypass clusters stay rigid. The #59 protection rectangle, the bulk-capacitor reserves and the supports stay obstacles. The 18 POWER-* reserves are the TP load-wire lands themselves.

| Placement | Signal HPWL | Peak RUDY / p99 | 5 mm tiles > 0.7 |
| --- | --- | --- | --- |
| Header-anchored locality | 162 m | 1.39 / — | 682 |
| v3 module-spread + swaps | 105 m | 1.24 / 0.78 | 68 |
| JL with swaps (for comparison) | 35 m | 0.93 / 0.81 | 42 |

RUDY is the bounding-box wire-demand estimate divided by ideal four-signal-layer supply. It is a congestion screen, not a routing result. The core header positions are tied to their partner boards' headers by the straight harnesses, so they stay fixed.

## Stack: six layers

`scripts/pcbgen/cut_capacity.py` bounds the first native locality placement. Its worst line is y=177 (board frame), which 853 signal nets must cross.

| Signal layers | Ideal track capacity | Ratio to demand |
| --- | --- | --- |
| F.Cu + B.Cu (four layers with intact planes) | 942 | 1.10× |
| F.Cu, In2.Cu, In3.Cu, B.Cu (six layers) | 2,364 | 2.77× |

Four layers fall below the 1.5× margin used for the jack halves, so the core takes the same six-layer stack:

- F.Cu, In2.Cu, In3.Cu and B.Cu carry signals.
- In1.Cu is a continuous AGND plane.
- In3.Cu also carries the −12 V fill. A signal batch that splits the fill is rejected.
- In4.Cu is a continuous +12 V plane.
- +5 V is routed as 0.4 mm tracks.

## Current status

| Native check (KiCad 10.0.6) | Result |
| --- | --- |
| Outline / stack | 310 × 284 mm minus the 56 × 46 mm notch; six copper layers, 1.6 mm, 2 oz proposal |
| Footprints | 3,594 netlisted (8 DNP), 13,406 pads |
| Native open edges | **1,402**: +12 V 80, −12 V 80, +5 V 0, AGND 213, signals 1,029 |
| DRC errors / schematic parity | **0 / 0** |

`scripts/pcbgen/route_jack_grid.py` ran these stages:

1. ±12 V plane fanouts and rail links (7,355 → 5,977).
2. A negotiated (PathFinder) pass over all signal nets on a 0.075 mm raster with two workers, finalized at its saved state (→ 2,975).
3. Rip-up-and-reroute batches rrr-01..08 (→ 2,077).
4. Signal batches signals-local and signals-01..09 (→ 1,843). AGND rose from 121 to 198 because new signal copper cuts the surface pours; AGND stitching reconnects them later.
5. Neck-down rule areas at 326 IC pad fields (0.15 mm track and signal clearance inside each IC's pads plus 2 mm, from `design/partition/neckdown-areas.json`), then rip-up-and-reroute rrr-01..24 in eight area shards on CI (1,841 → 1,789).
6. Signal batches signals-local..signals-40 in eight area shards (→ 1,776), signal escapes (→ 1,682), AGND stitching (→ 1,536) and a second signal-escape pass (→ 1,526).
7. With in-place stage checks fixed to load the board's own project (#183) and verified on a fresh copy (#181): rip-up-and-reroute in eight area shards (→ 1,523), signal batches in eight area shards (→ 1,516), AGND stitching (→ 1,513) and signal escapes (→ 1,509).

Each stage is applied to a disposable copy and checked with native DRC, schematic parity and zone refill. A stage is kept only when native open edges fall. Stage receipts are in `boards/osc-core/reports/grid-routing/`.

Still to run under #43: further rip-up rounds and hotspot-region renegotiation for the remaining signal edges, and ±12 V rail escapes.

The renders below predate the accepted 1,402-edge revision. Native receipts and the table describe current copper.

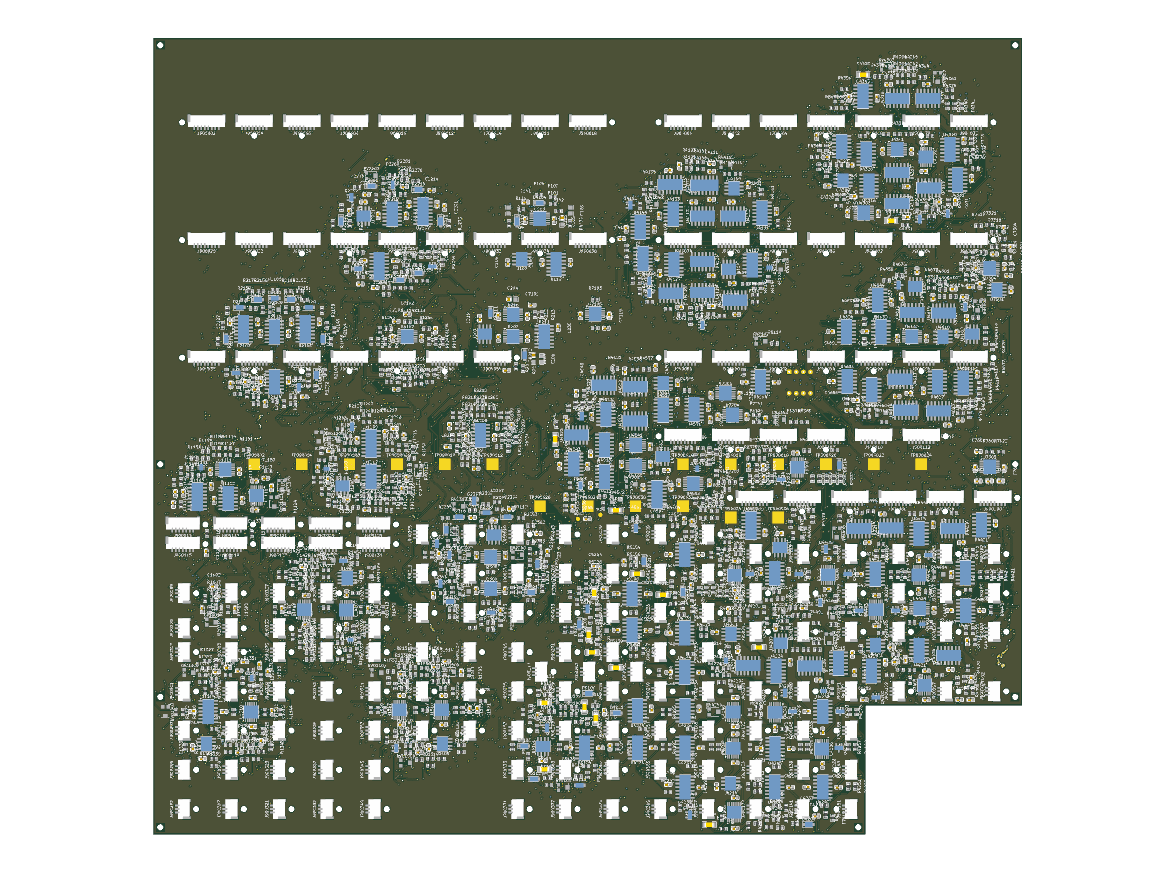
[picture p30: doc/public/assets/osc-hole-field/osc-core-top.png]
Core top: unvalidated routed draft in progress


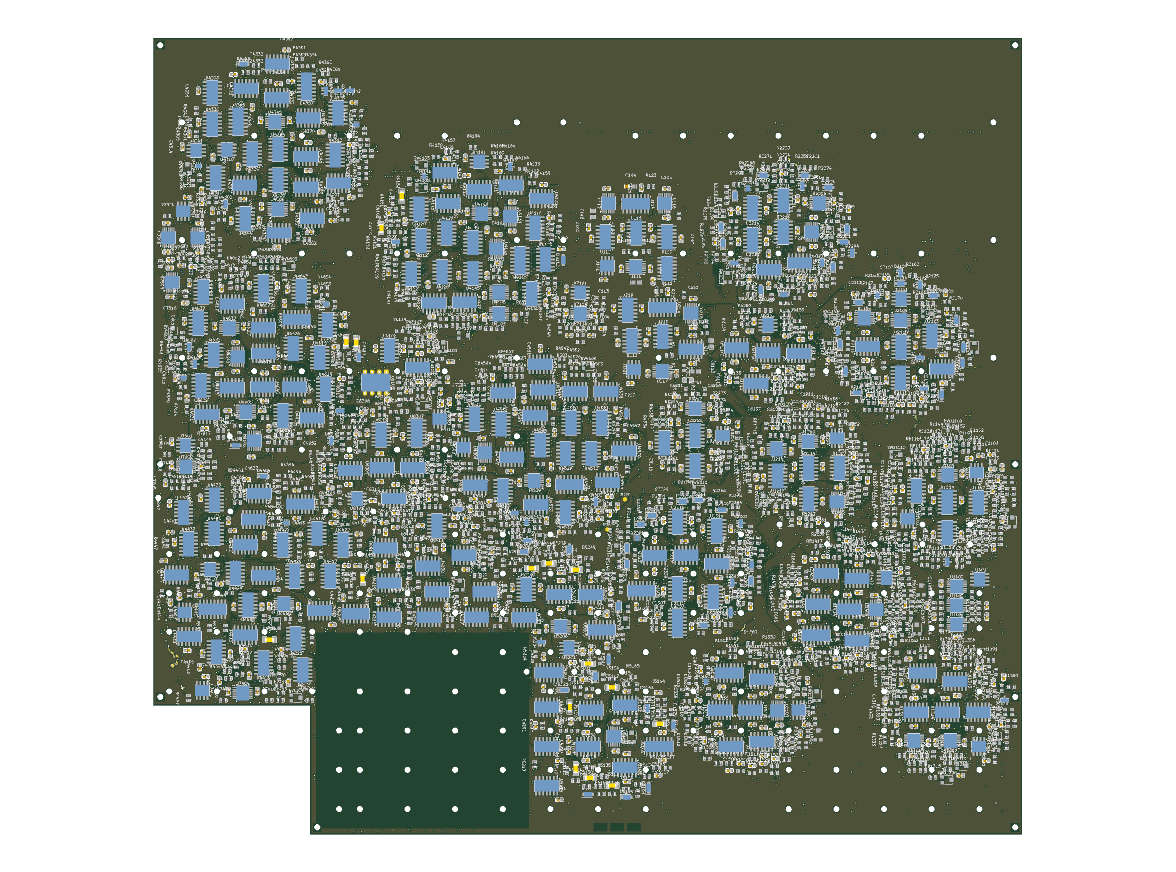
[picture p31: doc/public/assets/osc-hole-field/osc-core-bottom.png]
Core bottom: unvalidated routed draft in progress


## Qualification remains NOT RUN

The earlier field-solver ground/current extraction is parked and is not a routing gate. Rail and return resistance, the ≤0.5 mΩ combined AGND neck and hot distribution drop remain unqualified. So do the 2.1 A / 2 A / 0.5 A load-wire terminal transfers and GH contact current. Protection (#59), source/inlet (#57) and installed fit (#65) also remain open.

## Issue #189 implementation checkpoint

[Merged PR #190](https://github.com/Takazudo/zudo-osc-hole-field/pull/190) preserves
the canonical 1,509-edge core after its identical-input obstacle comparison in [37824207235](https://github.com/Takazudo/zudo-osc-hole-field/actions/runs/37824207235).
No unfinished job result is counted as progress.

The separate eight-shard run 37775496177 reached a reported 1,400 edges but worsened
AGND from 252 to 272 and failed to push its oversized filled board. Its exact
copper deltas and artifact digests are preserved under
`circuit/routing/issue189/concurrent-core/`; they are **not adopted**. The next
native pilot must repair affected returns, retain connected pad groups, reject
new warnings and agree after independent reload. A cache-free publication path
is prepared for the storage limit, but requires native refill equivalence before
use. No zone definition, physical constraint or successful copper is discarded.
#189 remains open; source replay is not hardware qualification.

### Issue #189 resumed native results (2026-10-09)

The identical-input core comparison finished: both old and corrected routers
reported 1,509→1,499, but both split two existing AGND pad groups and were rejected.
The subsequent recovered-copper plus stitching transaction reached 1,391 with
zero rule/parity errors and independent-copy agreement; it still split four
previous AGND groups, left AGND at 263 versus 252, and introduced hole-to-hole and
dangling-via warning identities. It was not adopted. That candidate did not change canonical core.

A source-defined local replay now omits ten suspected ground-splitting net
changes and repairs the overlapping signal-via cluster without changing layer or
electrical constraints. Native replay 37872907194 finished at 1,400 but was rejected: three original
AGND groups split into four extra pieces. Errors/parity were 0/0 and fresh
connectivity agreed. Newly reported hole-warning identities involved unchanged
original geometry; KiCad 10.0.6 caps each warning code at 199 records, so inventory
changes require investigation and are not waived. Exact evidence is retained in
`circuit/routing/issue189/core-reviewed/native-result-diagnosis.json`.

[Native replay 37881591885](https://github.com/Takazudo/zudo-osc-hole-field/actions/runs/37881591885)
finished at 1,430 edges but was rejected for two original AGND-group splits.
It retained all 132,953 original copper objects and added 317 outer-layer segments;
native errors/parity were 0/0, no new warning identities appeared, and fresh-copy
connectivity agreed. The lower count therefore is not accepted progress.

The filtered follow-up, [run 37895925149](https://github.com/Takazudo/zudo-osc-hole-field/actions/runs/37895925149),
passed all native gates and adopted **1,509→1,441**. Its 56 net transactions add
216 outer-layer segments while retaining all 132,953 existing copper objects.
No original pad group splits, new warning identities, DRC errors or parity errors
remain in this transaction; independent fresh-copy connectivity agrees. The 619
existing warnings remain unresolved. Removing derived fill-cache fields for
publication passed native refill equivalence for connectivity, warnings and geometry.
The published board SHA is `a0e3cff1ebc211564b8be10f6a993d50fb6d4372edde86a056ebc8dda3ea5932`.

### Accepted ground continuation (2026-10-10)

[PR #218](https://github.com/Takazudo/zudo-osc-hole-field/pull/218) adopted
**1,441→1,402** after
[run 38011194282](https://github.com/Takazudo/zudo-osc-hole-field/actions/runs/38011194282).
The transaction adds 344 segments and 38 vias, retains all 133,169 old copper
objects, and makes no cuts or component moves. AGND falls from 252 to 213;
signal and supply counts are unchanged. All 3,807 nonrouting board objects and
original connected pad groups are preserved. Native DRC/parity are 0/0, and
fresh-copy connectivity agrees.

The complete native warning audit preserves 1,407 hole-warning identities,
checks 382 added-copper fixtures and 42 paired-zone fixtures, and preserves all
1,827 complete findings on both sides. The ordinary capped report still contains
619 findings; that smaller number is not a complete warning inventory. Removing
derived fill-cache fields for publication passes native refill equivalence.
The current published board SHA256 is
`fa60b4e1587a67501782fb55374f0e5d5133f65cd0bbe62624aef502441fda10`.

Continue from this accepted board and preserve its 133,551 copper objects.
[PR #222](https://github.com/Takazudo/zudo-osc-hole-field/pull/222) has a separate
118-segment supply replay under native evaluation; its unfinished run is not
accepted routing progress. [PR #227](https://github.com/Takazudo/zudo-osc-hole-field/pull/227)
corrects an implicit plane-search budget cap while retaining the default budget.
Its identical-input larger-budget comparison still finds no route and changes
no board. Exact digests, checks and continuation commands are in the
[immutable routing checkpoint](https://github.com/Takazudo/zudo-osc-hole-field/blob/f920d594ab6a435c2523e3605c15f64b055b799e/circuit/routing/issue189/current-native-checkpoint.md).
Issue #189 remains open; these are incomplete routed drafts, not hardware qualification.
