Takazudo/zudo-osc-hole-field/doc/src/content/docs/verification/osc-pcb-control.mdx

---
title: "Control PCB routed draft"
description: "Reproducible control-board copper, connected ground contacts, and the remaining qualification work."
---

The shared control board now has a reproducible **routed, unvalidated candidate** at `boards/osc-control/osc-control-routed-draft.kicad_pcb`. Its 418 source packages and 36 supports preserve all 139 fixed control positions. The two complete slew circuits remain beside their unchanged potentiometers; all four amplifier bypass capacitors are 2.2975 mm from their supply pads.

The candidate uses the reviewed local edge tab beside RV601 and separate reservations around the six power terminals. It remains separate from the canonical partition outline. The tab and neighboring octave adapter pass their conditional source-envelope screen; installed fit remains unqualified.

| Current native check | Result |
| --- | --- |
| DRC violations, including silkscreen | **0** |
| Schematic parity findings | **0** |
| Source track segments / through vias | 4140 / 527 |
| Connected source ground contacts | **344 / 344** |
| Connected local IC/bypass rail pairs | **16 / 16**, maximum pad distance 2.535 mm |
| Complete native open-edge count | **0** |
| Independent reload and refill | Same ground and open-edge counts |
| Native routing / electrical and physical qualification | **Complete / NOT RUN** |

The earlier assignment of 123 complete K/P header pairs to existing identical sites remains. The current correction moves ninety envelope debounce passives into thirty complete resistor/resistor/capacitor groups beside their existing Texas Instruments SN74HC14DR inputs. All ICs, bypass capacitors, headers, panel controls, component identities and electrical net assignments are unchanged. Native comparison checks all 1,740 pads and confirms that exactly the 180 passive pads move.

The largest debounce-capacitor to input-pad distance falls from 144.626 mm to 7.665 mm; the median falls from 93.580 mm to 4.039 mm. The 8 mm input and 4 mm neighboring-resistor limits are project layout targets, not manufacturer requirements. These straight-line pad distances do not establish routed length or functional performance. The proposal is explicit in `design/partition/control-debounce-locality.json`.

Moving these terminals invalidates affected routes. The previous 72-edge checkpoint remains in git history. Rebuilding compatible copper and removing collisions produces a 199-edge seed, then checked routing reduces it to 0 open edges. Candidate links that disconnect ground are rejected. All 344 ground contacts, all 81 source AGND copper objects and sixteen local bypass pairs remain connected after independent refill. The six main-terminal arrays and local C222 ground stitch remain; their current and resistance capability is unqualified. Later inner-layer searches also consider distant rail islands; search distances do not establish electrical resistance or voltage drop.

All 418 visible references retain 1 mm text and checked clearance. Some moved passive references require offsets up to 16.553 mm. Native source replay, DRC, complete connectivity and independent refill form the acceptance gate for this draft copper. Current and resistance limits have not been checked for it.

The merged 43-edge checkpoint is preserved. A further bounded autorouter run timed out; its raw 30-edge candidate disconnected two grounds. Selectively retaining seven improved signal nets restored all grounds at 36 edges. Native-checked inner-layer rail and signal links then reached 23. Proposed routes that violated unplated-hole clearance or disconnected ground were rejected.

From 23 edges, checked multilayer links and a grid A* router over all four copper layers closed every remaining connection. They added the +12 V and -12 V feeds from the terminals to the op-amp cluster at the 0.4 mm rail width, the last +5 V pins, four long panel-signal links and three boxed pin escapes. Those escapes required rip-up and reroute of four nearby signal nets; all other earlier copper is unchanged. Four added AGND stitching vias rejoin rear ground-pour islands that new links cut. Each batch passed native DRC, parity, independent refill and the ground and bypass checks before adoption.

## Native layer views

These are copper/silkscreen previews of the routed draft, not fabrication plots or proof of physical fit. The rear view is mirrored to show the board from that side. Internal-layer routing is present in the PCB source but is not shown in these external-layer views.

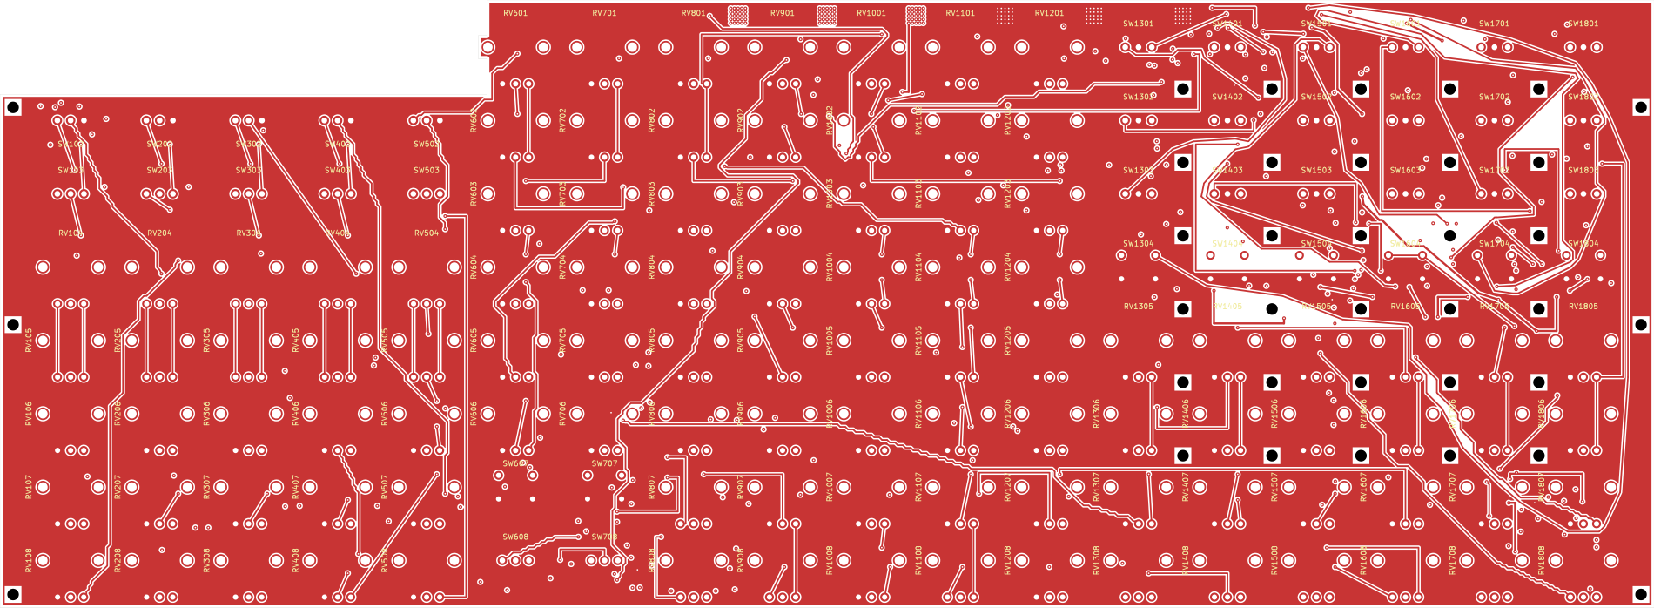
[picture p32: doc/public/assets/osc-hole-field/osc-control-copper-front.png]
Routed draft control PCB front copper and references


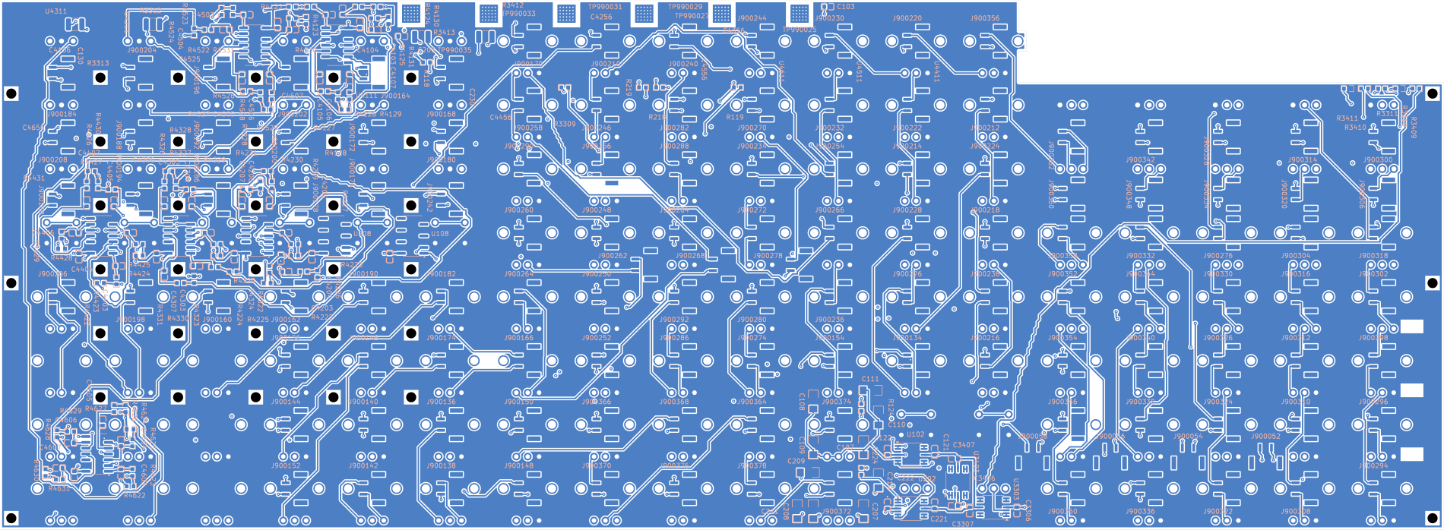
[picture p33: doc/public/assets/osc-hole-field/osc-control-copper-back.png]
Routed draft control PCB rear copper and references


## Remaining work

[Issue #39](https://github.com/Takazudo/zudo-osc-hole-field/issues/39) remains open for canonical geometry adoption; native connectivity of this draft is complete. The proposed four-layer, 2 oz, 1.6 mm stack, actual connected-copper current and resistance limits, exact protection and supply boundaries, manufacturing process and installed assembly remain unresolved under [#38](https://github.com/Takazudo/zudo-osc-hole-field/issues/38), [#59](https://github.com/Takazudo/zudo-osc-hole-field/issues/59), [#55](https://github.com/Takazudo/zudo-osc-hole-field/issues/55) and [#65](https://github.com/Takazudo/zudo-osc-hole-field/issues/65). Historical electrical receipts are not reused for this copper. No fabrication or order files are generated.
