Takazudo/zudo-osc-hole-field/circuit/routing/issue189/jr131-d7411-four-layer/README.md

# Distinct JR131 four-layer alternative

The In2 D7411.1–U7409.6 proposal is native rejected because it splits C7523.2/R7331.2 from original AGND. Its entire geometry, settled native evidence and independent proof remain in jr131-d7411-in2/ and commitbda90b1. It is not adopted.

This proposal selects the distinct four-layer path from the same immutable eight-case screen:92segments/4vias,0cuts/moves. All8outcomes/diagnostics/geometries already reproduced exactly(PASS40s/PASS42s). prepare.py pins that original screen, router and actual merged JR131 board, asserts51402retained objects, and serializes the whole alternative with no cuts. The extra via is not assumed safe; native checks must establish every original group survives. No accepted board file, part placement, width, clearance or production/native gate changes.

Source main16a248fc1dee8a68f416207fa3fd098e4e0d6490; JR input7bb70ac47e12c8bb2e2362d78f7602bdf99c2a69214c68aebeef273b0ce11965. Read-only pilot: routing-benchmark.yml,board=osc-jack-right,local_repair=true,local_mode=coupled. restore_connectivity=false; any original ground/rail split rejects the entire proposal. Complete-warning fresh adoption gates remain mandatory after a positive pilot. Native result NOT RUN at this commit. Keep189OPEN; no fabrication or hardware qualification.

## Terminal native rejection

Run38029289707/source102c1a4f0278283bc8190dc1c51be5724ee2a2e4 rejects the distinct alternative for the same C7523.2/R7331.2 AGND split(978filtered pads→976+2). Settled131x3→131x3; independentPASS46s verifies51402old+92segments/4vias,0cuts/moves,1080nonrouting unchanged,0DRC/parity,520raw warnings. Candidate0ea77e998858b628ade90d4429c62b1967ba8a23d939ee04a0e613cf6a706faf. Artifact11661452038,19756913bytes,SHA2567397729cb9fe8f4e73de1d6ab6292aed4ed05e153c93ecadc92d80b1cca26a0b. No fresh or full-warning stage followed rejection; neither passed. Do not adopt or redispatch unchanged geometry. No JR native worker remains active at this checkpoint.
