Takazudo/zudo-osc-hole-field/circuit/routing/issue189/jr131-d7411-last-via-avoid/README.md

# JR131 alternative avoiding the shared last via

Both earlier D7411.1–U7409.6 routes are native rejected for the same C7523.2/R7331.2 ground split. They share first/last via positions. Six bounded same-input trials exclude the first,last,or both sites for In2-only and four-layer searches. These are search-only via exclusions, not physical keepouts or a claim that a via alone caused the split. All original copper,clearances,widths,neck rules,-12V fill guard,0.025mm lattice,300000bound and6mm window remain.

GuardPASS33s. Avoiding the first site or both sites fails in both domains. Avoiding the last site produces the same whole path in both domains:167segments/5vias. prepare.py checks identical path/geometry between those two results, selects the In2 namespace, pins base/router/screen and51402retained copper, and emits proposalde6f086a535bd61cc5ec2791cd31021c7cedb614eec40fc6d7e5e4ca3a5cc74c. Zero cuts,moves,physical keepouts or board changes.

Source accepted main16a248fc1dee8a68f416207fa3fd098e4e0d6490 hasJR131 and all-five post-main38028250566PASS. Inputboard7bb70ac47e12c8bb2e2362d78f7602bdf99c2a69214c68aebeef273b0ce11965; saved native dumpa9f1b738f0e541ca5f01d7057f7bb002289e0bf43b90cb223253287f4e5abd84 from artifact11659542859(SHA2569ce87e2b7817faae8b6bbf4c7414214cc373ab58604134ec64a90142880f0f2a). Probe.py accepts that extracted dump path and replays the6cases; prepare.py serializes the selected complete proposal.

Next gate is one read-only native pilot on this isolated source: routing-benchmark.yml,board=osc-jack-right,local_repair=true,local_mode=coupled. restore_connectivity=false; any original native group split rejects the whole candidate. Require all51402old copper,unchanged physical/electrical context,settled/fresh connectivity and zero DRC/parity errors. Even a positive pilot still requires full source-bound warning audits and fresh adoption replay. Native result NOT RUN at this commit. Keep189OPEN; no fabrication or hardware qualification.

## Native pilot reconciled; full adoption still required

Run 38031328950 at source 790c75f851e15fe76052b6aa1e6f4c6a133025dc completed. Artifact 11662171680 (29,664,589 bytes), ZIP SHA256 3115f9948613136ad4f6c6ef134a60a42a09e579d5c55c844bf2279a1eaeaf6c. Independent heavy-guard reconciliation PASS in 56 seconds: 131/131/131 base, 130/130/130 candidate and fresh. Candidate/fresh PCB SHA256 e06b7471ddc8f5c8c498c5eb5bf8655cc6de539e92826a5701cf1de06356e136. All 51,402 old copper objects retained, exactly 167 segments and five vias added, zero cuts, 1,080 nonrouting objects unchanged. Native DRC/parity errors zero; no original pad group splits or new raw warning identities. Raw warnings remain 520; capped categories are not complete-warning evidence.

`prepare_adoption.py` pins that proof, source board and proposal, serializes through the pinned native toolchain, and checks the exact geometry/UUID delta. Workflow choice `d7411-last-via-avoid` requires complete-native-warnings, native-zone-batch-size 16 and a 120 minute command limit. The executable dispatch regression failed before adding the choice, then passed; all 19 workflow/scope/copper-identity tests and circuit evidence validation passed. An initial test invocation used the system Python without Shapely and failed import; the established route virtualenv passed all 19. Full adoption and complete warning checks remain unrun at this commit. Canonical main remains JR131.
