Takazudo/zudo-osc-hole-field/circuit/routing/issue189/jl118-r8127-via-branch/README.md

# JL118 R8127 bounded via-branch repair

A distinct three-object cut removes one nearby signal via and its two attached full segments within12.11×13.21mm. The ground-only screen finds one full-width segment. A separate provisional endpoint restoration finds six additional objects, giving a seven-object joint candidate (six segments/one via), but this is not native acceptance.

The read-only native cut pilot derives real cut components before routing. Both retained endpoint obligations, F.Cu(256.8,100.9)mm and In2.Cu(256.7,100.5)mm on XDFE73EDB3AA45015AAD2, must reconnect; no padless retained fragment may be discarded. The pilot cannot write canonical copper. Original groups, exact cuts, all uncut copper, complete warnings, DRC/parity and fresh-copy gates remain required for eventual adoption. No placement, panel, layer or electrical constraint changes.

Source input a01df89dcab3d4fab8eb0ae80195b2825d2d47adc517cd73452d9b9aa6ea079a; saved native dump9d193cd974148e58b576d247edb5bce804f06a29d075098513a1292c21fbf136. Provisional joint proposal SHA256e691e431345bdd84fa86919be8b42704226620f7c8fd0921c457176fc07cd6f1. Its native cut memberships have not yet been established; do not promote it from raster evidence.

The previous R8107 native pilot38036682185 is terminal/rejected and independently reconciled; it is not rerun. This candidate has different exact cuts, victim net and bounds. Run the existing routing-benchmark workflow with board=osc-jack-left,local_repair=true,local_mode=cut against this source. Issue189 remains OPEN.

Native cut pilot38037812466/source46b8562ca57f1b73ade36f48a35188b4be60be15 is terminal, independently reconciledPASS72s. Artifact11665246229,ZIP SHA2566293e6bfe4e4d578087cae389a35c2662a4ea68fe1851f614dafb191e809f732. Baseline118/AGND15; cut118/AGND14 with two victim components; automatic victim restoration returns118/AGND15. It adds4objects after3cuts, retains all33418uncut objects/1111nonrouting,0DRC/parity,477unchangedwarnings,freshagreement. No gain, so not eligible.

The exact native cut has13/52members on the victim net. The two retained boundary tracks belong to different components and their union covers every original victim pad. This establishes the native obligations for the pinned seven-object joint proposal, which explicitly reserves a ground segment before restoring the two boundaries. The full adoption dispatcher requires complete warning inventories, batch16 and the exact reviewed cut plan; no ordinary raw-warning-only adoption is used. Fresh native acceptance of this joint proposal remains pending. The prior native pilot is not redispatched.

Replay the provisional comparisons with `python endpoint_screen.py --dump SAVED_NATIVE_DUMP --output OUTPUT.json` from the repository root, using the full script path. source-screen.json is the exact pinned32case prefilter; the script checks canonical board and dump hashes before routing. The ground-only and joint raster outputs remain predictions.
