Takazudo/zudo-osc-hole-field/circuit/routing/issue189/reviewed-cut-warning-audits/README.md

# Complete warning evidence for bounded reviewed cuts

The full native warning path previously rejects any removed copper through its additive-only mask/zone scope. A new cut repair must not bypass that rejection by turning off complete warnings. This change retains additive-only behavior unless the caller supplies an exact source-bound bounded repair plan with `--reviewed-cut-plan` and `--complete-native-warnings`.

The plan must match the original board SHA and board ID; it must name one open target and one to twelve unique whole signal cuts within at most50×50mm, with at most two victim nets, under the existing repair scope rules. Actual removed UUIDs must equal that set. Every uncut copper block, duplicate historical object multiplicity and nonrouting object remain identical. Reusing a removed UUID, modifying an old object, losing an undeclared object or changing project/rules fails closed.

Both complete hole inventories still run. The only permitted vanished hole is the exact old via named by a reviewed cut; no footprint hole, unrelated via or replacement under an old UUID can disappear. Every added copper object still receives a native silk fixture, and every changed outer-zone interaction retains complete paired native artwork evidence. Mask healing, custom audited-domain rules and unsupported geometry remain rejected. Cut zone fixtures cannot resume from an older audit. The full original connectivity, DRC/parity, new-warning, fresh-copy and publication gates remain unchanged.

This implementation authorizes no cut by itself. Its native worker integration validates the source plan against native baseline geometry and exact final replay. The earlier R8107 cut pilot is an explicit negative control: ground improves but its victim remains split and both retained endpoints dangle. Its full-board promotion gate must remain false.

Validation: two new regression tests fail against the old API, then63 targeted scope, retained-copper, hole, paired-zone, dispatch and promotion tests PASS. Saved JR130 complete native proof replays exactly unchanged; the R8107 native negative control accepts only its explicit three-cut geometry scope but still fails its original promotion gate for a split victim and two dangling endpoints (guardPASS77s). This replay does not rerun the native oracle. Circuit checks before/after PASS. Complete native fixture production for a cut transaction is NOT RUN until the next exact remote adoption; local pinned10.0.6 image unpack remains blocked. No board or physical/electrical requirement changes. Issue189 remains OPEN.
