Takazudo/zudo-osc-hole-field/circuit/routing/issue189/jr-neighbour-return-repair/README.md

# Explicit restoration of newly split native returns

The exact rejected three-signal candidate e2cd1e974ff1fd2353cd6c9b09e50c4d044ac8268373de80ca2294c0d06c1866 has four new return obligations against original native pad groups. `probe.py` tries direct and plane connections with full0.3mm tracks,0.6/0.3mm vias,0.25mm clearance,0.025mm grid,300000expansion bound and6mm frames, retaining all copper. Eight modes completed (guardPASS26s), with only the U7607.5/C7615.2/C7622.2 ground group finding a path: one0.425mm B.Cu segment and one via. The -12V plane mode finds the source already through-connected, not a repaired plane partition; it is correctly not counted as a repair.

There is no complete four-return transaction. `prepare_joint.py` therefore isolates the whole D7604.1–D7603.1 signal proposal and adds that exact ground repair. The other two whole unaccepted signal cases are omitted, never removed from canonical copper. Final proposal74segments/5vias, zero cuts or placement changes, minimum new signal-to-ground gap4.079276mm. This is a changed joint proposal, not proof of native eligibility. Preserve all51177old objects and require all original groups, native DRC/parity/warnings, settled/fresh repeats and complete capped-warning evidence. No automatic restoration or canonical publication occurs in the pilot.

## Ordinary native pilot passed; full warning evidence still required

Read-only38015774133 at0867a05a01f321d890847c5fa4b1bd6a8d6e866d completes baseline134/134/134, candidate133/133/133 and independent fresh133/133/133. Artifact11656122445 SHA256a42f92f62ba59b71b9321e0e1dce50e47c468ef5039c5fc49c5b236744ca9365 passes independent reconciliation (guardPASS75s): all51177old objects retained, exact74segments/5vias added,0cuts,1080nonrouting objects unchanged,0DRC/parity errors,520raw warnings/no new reported identities, no original groups split. Native candidate/fresh22189b127579271b2f2c219da5e4b7e2af59673cb04e002b0dc4966afe2170dd; replayc4b7910f964b56f9231bf6dd3e21b07b4ce8c8bbca430f09f80ea08acdd34411.

This is NOT canonical adoption. Both silk categories hit199 in the raw report, so the dedicated `d7604-return-joint` adoption replay requires all four complete native audits with paired zone batch16 inside the existing full gate. `prepare_adoption.py` checks the independently reconciled pilot, current source/proposal hashes, exact79serialized additions and zero removals. Native command bound120minutes; existing settled/fresh, membership, retention and publication checks remain.28 workflow/merge/complete-warning regressions pass, including actual shell dispatch argument tests for mandatory audit flags and unchanged legacy behavior. Native serialization and full audit/adoption are still to run on this new source.
