Takazudo/zudo-osc-hole-field/circuit/routing/issue189/jr134-plane-window-diagnostic/README.md

# Cause-driven plane fanout window comparison

The paired-movement failures exposed a separate search-domain limit: plane fanouts hard-coded3mm even when the component-routing window was6mm. `route()` now accepts an explicit positive finite `plane_window_mm`, retaining the3mm default and all existing clearances, dimensions, keepouts, layer and native gates. A regression proves that6mm can reach a legal site beyond a via-only keepout that excludes the default window, without crossing that keepout with a via. Invalid windows reject.32 router and15 bounded/driver tests pass.

`diagnose.py` reconstructs the exact existing raster via tests on saved JR134 input SHA256f885375bc4a8ac5cc0ca879f841a4d3768a560876e43c023e2abe14e38a86c8a. The six recorded no-site paired cases have zero3mm goals and5442–6443 goals at6mm. Unmoved R8490 has0→6384; unmoved RB4615 has17→5503. Counts are not paths or native proof. Individual-constraint omission counts are diagnostic attribution only; no constraint is omitted in routing. The first diagnostic failed on a metadata typo (`type` instead of `kind`), then passed after correction. A final run binds an unchanged router hash for the entire diagnostic.

`route_window.py` compares3mm/6mm on identical unchanged native inputs, with the same16mm allocation,0.0125mm grid,300000 expansion limit,0.3mm ground track,0.6/0.3mm via and0.25mm clearance. All four are negative (guardPASS28s). R8490 changes from no legal site to search exhausted at21187 expansions; RB4615 exhausts43982 states at both sizes. The larger window therefore does not solve either escape. No changed placement, removed copper, PCB output or native pilot was submitted. Do not repeat these settings unchanged or treat untested paired6mm cases as completed failures.

Reproduce with the route virtualenv, passing the saved JR134 dump to each script through the required heavy guard. `result.json` and `route-result.json` pin board, dump and router hashes. This is bounded failure attribution, not physical impossibility or hardware qualification.
