Takazudo/zudo-osc-hole-field/circuit/routing/issue189/jr-rb4413-move/README.md

# Disposable RB4413 movement pilot

Same-input virtual comparison on accepted JR134 found a complete route after a source-defined movable resistor translation [0,-0.2]mm; the unmoved direct control failed. The proposal retains all old copper and adds six full-width segments and one 0.6/0.3mm via. RB4413 is not fixed or in a bypass cluster; orientation and side remain unchanged. Plan/proposal/source hashes bind the experiment.

`pilot.py` runs only with pinned KiCad10.0.6. It checks the settled baseline, moves only RB4413 in a disposable copy, applies the exact reviewed copper and checks settled/fresh native DRC, parity, warnings and all original pad memberships. Canonical board and source floorplan hashes must remain unchanged. No publication path exists. A positive gate remains provisional until independent full-block retention and physical-delta reconciliation plus deterministic source regeneration pass. The source floorplan is generated by scripts/checks/partition35_floorplan.py; do not hand-edit its generated JSON for adoption.

Worker execution uses the existing read-only local-pilot job on an isolated immutable worker branch. No core worker is changed or duplicated. Source regeneration/native placement checks remain NOT RUN until explicitly recorded.

Pilot37986929982 is complete and rejected:134→134, one original signal split and a new dangling-track warning. Full SHA-verified artifact and independent native physical/copper proof are in download.json and native-result.json (guardPASS25s). Only the reviewed footprint translation differs; all51177old copper objects retained,7new,0cuts,0DRC/parity,fresh agreement. The exact old-edge landing diagnosis and changed additive repair are in sibling jr-rb4413-edge-bridge/.
