Takazudo/zudo-osc-hole-field/circuit/routing/issue189/jr134-movable-ground/README.md

# JR134 bounded source-defined movement comparisons

Nine movable resistors outside bypass clusters were screened against the same saved native JR134 input. Each screen checks 1,680 translations within ±2mm at 0.1mm steps, unchanged orientation/side, the fixed source outline, 0.35mm courtyard spacing, 0.25mm copper clearance and a full 0.2mm additive signal bridge. Existing copper is retained. R7609 and RB4613 have no compatible translation; the other seven have 30 candidates total. This is a conservative static screen, not native placement acceptance.

Routing compares every compatible translation against an unmoved control using either a direct AGND join to the existing main group or native-plane-targeted raster fanout, within a fixed 16×16mm frame at 0.0125mm resolution and 300,000 expansions. The -12V fill guard remains enabled. Partial signal bridges are not submitted. Run `screen.py REF` then `route_screen.py REF` with the numerical virtualenv under the shared heavy guard. Exact saved input hashes are retained in each result.

No physical component, copper or canonical board has changed. Any positive virtual proposal still requires source regeneration and native10.0.6 DRC, parity, complete warning, original group-membership, retained-copper and settled/fresh gates. The guarded comparison completed in257seconds:67trials,66negative and one complete virtual route. RB4413 moves by[0,-0.2]mm and adds six segments plus one via, including the full-width signal landing bridge. Its unmoved direct control failed. The search stops at its first complete candidate, so untested later RB4413 translations and plane mode are not claimed negative. Exact per-reference results and hashes are in summary.json.
