Takazudo/zudo-osc-hole-field/circuit/routing/issue189/jl118-r8127-placement-screen/README.md

# R8127 larger physical-movement comparison

On exact accepted JL118, all1,680 translations at0.1mm steps within±2mm preserve orientation/side and are screened against the fixed outline,0.35mm source courtyards,0.25mm copper and a full0.2mm additive signal landing bridge. Only the same seven translations from the earlier±0.8mm screen remain feasible. The expanded physical scope yields no new placement candidate, so the unchanged routing comparisons are not repeated. No footprint moved and no native placement result is claimed.
