Takazudo/zudo-osc-hole-field/circuit/routing/issue189/jl-r8276-placement-screen/README.md

# Bounded movable R8276 comparison

R8276 is source-defined movable, F.Cu, outside bypass clusters. Of288translations within±0.8mm,14pass exact JL outline,0.35mm courtyard,0.25mm copper and additive0.2mm signal landing bridge checks. The unmoved same-input control and all14translations fail complete ground routing, both In1plane fanout and direct routing at0.0125mm/300k. GuardPASS39s/44s. All copper remained fixed; no placement changed, no partial proposal submitted, no native moved-board result claimed. Do not retry unchanged scopes.
