Takazudo/zudo-osc-hole-field/circuit/routing/issue189/core-short-no-via/README.md

# Short outer-layer core signal candidates

Eleven saved cases contribute19outer-layer segments with zero vias/cuts; each case is at most four segments and4mm total. All source/result hashes and conservative new/new clearance proof are in selection.json. This is an original-input raster proposal only. Wait for core37936741388 and any subsequently accepted ground batch, rebase against actual accepted copper with full retention/clearance checks, then use unchanged native acceptance gates. Do not count these as accepted joins or launch a competing core writer.

Static comparison against the pending38-group ground proposal passes for all11signal cases (minimum gap2.1367392955mm). This is not an accepted-input rebase. After core37950004600 is terminal and fully reconciled, `rebase_proposal.py --accepted-sha256 ACTUAL_HASH` permits only the exact whole382-object ground addition or unchanged core, preserves all original full copper blocks, and rejects unknown changes or clearance conflicts. Do not run it on a pending result. Fixed workflow choice short-no-via then uses native serialization and all ordinary gates.
