Takazudo/zudo-osc-hole-field/circuit/routing/issue189/jl-u1518-joint/README.md

JL U1518 cut pilot37956537948 rejected120→120 because signal restoration reblocked ground. This joint raster experiment first reserves an explicit full-width ground path, then reconnects both actual native-cut victim components. The first declared signal order yields a complete58-segment/no-via proposal with the same four reviewed cuts. Search uses F/In2/B,0.0125mm,300000cap and the original finite frame; guarded run passed in6s. Only the complete fixed proposal is submitted for a strict native pilot. Retained-endpoint warnings, original pad-group membership, DRC/parity and fresh agreement remain mandatory. No canonical copper is changed or acceptance claimed by the raster result.

Pilot37958624929 is pinned to source161f734bd0319b0ce51a1e8d1331d0196ed416d0. Gated adoption preparation is available in prepare.py/adoption-plan.json and workflow choice u1518-joint, but must not be dispatched before native pilot eligibility is fully reconciled. The fixed replay checks exact input/proposal/add/remove identities and copies original .kicad_pro/.kicad_dru before applying cuts. Native serialization/adoption is unrun.
