Takazudo/zudo-osc-hole-field/circuit/routing/issue189/jr-r4207-joint/README.md

Native cut pilot37956542080 rejected136→136 because restoring the signal reblocked ground; all51059uncut objects survive,+3/4reviewed cuts,0DRC/parity,520unchanged warnings,no original splits,fresh agrees. The joint raster search reserves explicit ground then restores both native victim components. Initial setup failed because it assumed both components had retained track endpoints; native topology actually has one bare D1401.2 pad and a96-object connected component. The corrected setup explicitly verifies that topology and uses both full native groups. It completes86objects/one via with the same four reviewed cuts on F/B0.025mm; heavy guardPASS4s. No retained track endpoint shares a removed segment endpoint in the exact endpoint screen. Native warning checks remain authoritative. Only this complete proposal is eligible for submission to a strict native pilot, not canonical adoption. Prepared replay copies original project/rules and verifies exact input/proposal/add/remove identities; do not dispatch adoption before native pilot eligibility is fully reconciled.
