Takazudo/zudo-osc-hole-field/circuit/routing/issue189/core1441-no-via/README.md

# Bounded core outer-layer signal screen

The exact saved core1441 native dump was screened for the first24 eligible nearest-component signal nets excluding active U1513, with F.Cu-only and B.Cu-only cases (48 total). Full original memberships remained in every search. Resolution0.025mm,300000-expansion cap,weight1,frames at most100mm,unchanged signal/rail/ground rules. GuardPASS377s; recorded route time373.24s. Eleven positive cases on ten nets yield117segments and zero vias; no cuts. These are raster proposals, not native progress or proof all selected nets connect.

The separate core-short-no-via selector keeps seven short cases/12segments, at most four segments and4mm per case; minimum new/new cross-net gap19.5567mm. It remains pinned to the original1441 board and cannot be rebased or submitted until core37936741388 is terminal/reconciled. Ground batch remains the preferred next native core trial.
