Takazudo/zudo-osc-hole-field/circuit/routing/issue189/jl-u2204-endpoints/README.md

# Retained endpoint repair

The preceding native joint candidate is rejected for new dangling warnings on retained copper despite strict edge improvement and no original pad-group splits. This proposal retains that exact joint transaction and adds 2 outer-layer segments, 0.757106781mm total, no additional vias/cuts. All additions use the existing permitted0.15mm signal neck rule; no rail/ground neckdown is used. Each exposed retained endpoint is an exact endpoint of an added segment.

Search-only20um anchors lie inside the existing200um retained tracks. The anchor endpoint is identified by intersection with the reviewed removed-track endpoints, not the displayed DRC item position. No synthetic pads enter the physical proposal. Full native warning, original-group, DRC/parity and settled/fresh gates remain mandatory. A pilot cannot promote canonical copper.

Native pilot37945793199 is eligible:121→120,0DRC/parity,477unchanged warnings,no new identities/splits,fresh agreement. All33241uncut original objects are identical;53added/1reviewedcut. ZIP and candidate/replay hashes are in artifact.json. No canonical adoption yet; fixed replay must recheck all gates.
