Takazudo/zudo-osc-hole-field/circuit/routing/issue189/jl-u2204-ground-cut/README.md

# U2204 cut and outer restoration

Native37937518106 rejected121→121. One7.35mm B.Cu cut joined AGND18→17 but split U8213.3/J900027.1. Victim restoration on In3.Cu split−12V, so fallback dropped it. Rejected final has0additions/1removal,0DRC/parity,479warnings(two new dangling tracks),one unrestored signal group. Canonical121 unchanged. Verified receipt/artifact/replay/retention are saved here.

Exact native cut-topology probes found8B.Cu segments/no vias with F+B or B-only and no F-only path (guardPASS10s). The pinned B-only proposal includes the original cut and disables automatic repair in the coupled native pilot. All original-baseline gates remain mandatory; raster success is not adoption.
