Takazudo/zudo-osc-hole-field/circuit/routing/issue189/jl-u2204-joint/README.md

# Coordinated U2204 ground and victim restoration

The preceding8-segment outer restoration natively restored the signal but blocked ground again, leaving121edges; it was not adopted. This search uses the exact native cut dump and deliberately separates the original U2204 ground group only inside the search model, requiring an explicit permanent ground link before routing the signal victim. All original native memberships remain the acceptance baseline.

F/B-only finds a complete51-object candidate with3vias/1reviewedcut. F/In2/B restores ground but fails the victim and is ineligible. GuardPASS6s. Three new via centers pass the conservative0.85mm pair spacing. The fixed coupled native plan disables automatic repairs; all topology/warning/DRC/parity/fresh gates remain mandatory. No native acceptance yet.
