Takazudo/zudo-osc-hole-field/circuit/routing/issue189/jl-u2204-outer/README.md

# Outer-only U2204 native control

Run37940189931 checked8 B.Cu additions/1reviewedcut. Native121→121,0DRC/parity,477unchanged warnings,no split original groups,fresh agrees. Signal connectivity was restored, but AGND returned to18open edges: the new signal route blocked the temporary ground connection again. No strict improvement, so nothing adopted. All33241uncut original objects remain identical. Verified candidate/replay/artifact hashes and receipt are saved here.

The next distinct experiment reserves explicit ground copper first, then restores the victim against that occupied geometry. See jl-u2204-joint/. Its search partition is artificial only for requiring the explicit ground link; original full native memberships remain the acceptance baseline.
