Takazudo/zudo-osc-hole-field/circuit/routing/issue189/jr-u8303-endpoints/README.md

# Retained endpoint repair

The preceding native joint candidate is rejected for new dangling warnings on retained copper despite strict edge improvement and no original pad-group splits. This proposal retains that exact joint transaction and adds 3 outer-layer segments, 1.163908730mm total, no additional vias/cuts. All additions use the existing permitted0.15mm signal neck rule; no rail/ground neckdown is used. Each exposed retained endpoint is an exact endpoint of an added segment.

Search-only20um anchors lie inside the existing200um retained tracks. The anchor endpoint is identified by intersection with the reviewed removed-track endpoints, not the displayed DRC item position. No synthetic pads enter the physical proposal. Full native warning, original-group, DRC/parity and settled/fresh gates remain mandatory. A pilot cannot promote canonical copper.

Native pilot37945797248 is eligible:137→136,0DRC/parity,520unchanged warnings,no new identities/splits,fresh agreement. All51024uncut original objects are identical;39added/2reviewedcuts. ZIP and candidate/replay hashes are in artifact.json. No canonical adoption yet.
