Takazudo/zudo-osc-hole-field/circuit/routing/issue189/jr-u8303-ground-cut/README.md

# Native U8303 cut control

Run37940194109 rejected137→137. Two cuts temporarily joined AGND26→25 but split one original signal component (victim1→2open edges). Fourteen replacement segments restored that signal, but ground returned to26. Native0DRC/parity,520unchanged warnings,no split original groups,fresh agrees. All51024uncut objects remain identical. No candidate adopted.

The J900099.1 no-source-in-frame diagnostic belongs to a component already disconnected before the cut; full native topology retained it. The next joint search reserves a permanent ground link and then reconnects the two native pieces of the affected original27-object signal component. Every original outside component remains in the acceptance baseline.
