Takazudo/zudo-osc-hole-field/circuit/routing/issue189/jr-u8303-joint/README.md

# Joint U8303 ground and signal restoration

Native cut pilot37940194109 restored the original signal component but blocked ground again:137→137,0DRC/parity,520unchanged warnings,no splits,fresh agrees; not adopted. Its outside-frame J900099 component was already disconnected before the cut, so that diagnostic is not a lost original connection.

This exact-cut search requires an explicit ground link before restoring the two native pieces of the original27-object victim component. All original native memberships, including the remote component, remain the full acceptance baseline. F/B-only and F/In2/B both yield36objects/1via/2reviewedcuts (guardPASS6s). The fixed F/B coupled plan disables automatic repair and still requires all native gates. No native acceptance yet.
