Takazudo/zudo-osc-hole-field/circuit/routing/issue189/jr137-ground-cut-screen/README.md

# JR137 bounded cut prefilter

All24eligible source-pad cases completed (guardPASS65s), finding16ground-only paths. Each has at most12exact signal cuts on at most2victim nets,frame≤50mm and300000expansions. None is a complete proposal: native cut topology and victim restoration remain unchecked.

The first native pilot selects U8303.9:2F.Cu cuts on one victim net. Its saved ground path uses F/B only; native restoration also uses F/B to avoid the observed JL In3-plane regression. Complete original native memberships and all acceptance gates remain mandatory.
