Takazudo/zudo-osc-hole-field/circuit/routing/issue189/jr137-ground-refinement/README.md

# JR137 further ground raster refinement

All26 remaining AGND groups on native-acceptedJR137 were screened at0.00625mm with unchanged full-width ground rules and300000 expansions. No paths were found (guardPASS131s). No native proposal exists. The next distinct strategy is an explicit bounded signal cut followed by mandatory native victim restoration; do not repeat this unchanged configuration or just raise its cap.
