Takazudo/zudo-osc-hole-field/circuit/routing/issue189/jl121-ground-links/README.md

# JL121 bounded existing-ground links

All18 remaining native AGND groups were searched against the existing main ground component at0.025mm with full ground dimensions and300000 expansions. No paths were found; guarded execution PASS35s. No proposal or native acceptance exists. The next distinct method is a bounded explicit signal-cut prefilter followed by native victim restoration.
