Takazudo/zudo-osc-hole-field/circuit/routing/issue189/jl121-ground-refinement/README.md

# JL121 further raster refinement

All18 remaining native AGND groups were searched on the accepted121 input at0.00625mm, unchanged full-width ground rules and300000-expansion cap. No paths were found. Guarded execution PASS95s; no native candidate exists. Do not repeat unchanged or increase the cap; next distinct strategy is a bounded link to existing ground copper, avoiding a new plane-fanout via.
