Takazudo/zudo-osc-hole-field/circuit/routing/issue189/jr-two-fine-ground/README.md

# Pending JR ground pair

Nine additive ground objects from acceptedJR140: R8407.2 and U8303/C8329/C8318. Native NOT RUN. Wait for isolated R8487 run37933235474, verify its artifact/receipt and reconcile the actual accepted board before explicitly rebasing this saved proposal. Preserve all accepted copper and compare new-copper/drill compatibility; do not assume the pending R8487 proposal is accepted. Full original membership, warnings, DRC/parity and fresh-copy checks remain mandatory.
