Takazudo/zudo-osc-hole-field/circuit/routing/issue189/jr140-fine-ground/README.md

# Fine ground screen on accepted JR140

All28 remaining native ground groups were screened at0.0125mm, with bounded frames,300000-expansion cap and unchanged0.3mm ground/0.6mm via/0.25mm clearance. Two groups yielded proposals: R8407.2 (seven objects) and U8303/C8329/C8318 (two objects). The other26 found no route. Guarded run passed in78s. These are not native-accepted changes. Keep their exactJR140 base and wait for active R8487 isolation run37933235474 before any explicit rebase/compatibility check and next sole JR native dispatch.
