Takazudo/zudo-osc-hole-field/circuit/routing/issue189/jl125-fine-ground/README.md

# Fine bounded ground fanouts on accepted JL125

The earlier broad ground searches used coarser grids. This pass applies the established core fanout method at0.025mm to each of the22 actual remaining JL ground groups, with bounded frames,0.3mm ground width,0.6mm vias and0.25mm clearance. One group yields a proposal: C8143.2, one segment and one via. The other21 groups find no path. Guarded run passed in39s. Native acceptance is not inferred; selected replay is in ../jl-c8143-fanout/ and preserves the full original native baseline.
