Takazudo/zudo-osc-hole-field/circuit/routing/issue189/jr-r5273-ground-repair/README.md

# R5273 restoration on the rejected pair

Use the exact native rejected139 candidate from run37931910118. At0.025mm and0.0125mm, bounded plane fanout and direct-link attempts all find no route from R5273.2 at unchanged ground dimensions. Guarded run passed in15s. No combined repair proposal or native acceptance resulted; the accepted baseline remainsJR140. Isolated R8487 native replay is a separate diagnostic, not a claimed restoration.
