Takazudo/zudo-osc-hole-field/circuit/routing/issue189/jr-r8487-no-via/README.md

# Isolate R8487 from the rejected pair

Native run37931910118 joined both proposed signals but split R5273.2 AGND;140→139 was rejected. Remove the entire45-object U5213 transaction and retain only the27-object R8487 transaction. The lost pad is6.5666mm from U5213 copper and21.1693mm from R8487 copper; proximity is an inference, not proven causation. This isolated native run will test attribution. Zero vias/removals, same acceptedJR140 input. Do not count the rejected pair or this unrun isolation as progress.
