Takazudo/zudo-osc-hole-field/circuit/routing/issue189/jr-d7504-ground-first/README.md

# Ground-first reinforcement control

Before adding D7504 signal copper, test redundant ground fanouts/direct links from R7505.2 and R7530.2 on acceptedJR141. Artificially separate each source only for search; retain original native membership as the mandatory acceptance baseline. Eight0.025/0.0125mm bounded cases at unchanged ground width/clearance found zero routes. Guarded run passed in22s; no candidate or native acceptance resulted. This rules out the tested additive ground-first ordering, not every possible coordinated repair.
