Takazudo/zudo-osc-hole-field/circuit/routing/issue189/jr140-d7209/README.md

# Remaining D7209 on accepted JR140

Use the newly accepted D7208 copper and its immutable fresh native dump. Test the remaining D7209 obligation in the saved bounded frame on F.Cu only and F.Cu/B.Cu,0.025mm lattice, weight1,300000 expansions. Neither found a route; guarded run passed in8s. This is a changed-input follow-up, not an unchanged retry. No new candidate or native adoption resulted.
