Takazudo/zudo-osc-hole-field/circuit/routing/issue189/jr141-no-via-alternatives/README.md

# Single-layer alternatives on accepted JR141

Identical six previously positive short targets and saved bounded frames, each restricted to F.Cu or B.Cu,0.025mm lattice,300000 expansion cap, weight1. The guarded12-case screen completed in60s. Only D7208 yielded copper:26 F.Cu segments,zero vias. All other cases yielded no route. Current full native memberships and accepted copper remain intact; result.json records the immutable native input SHA and all failures. Selected replay is in ../jr-d7208-no-via/. This is not native acceptance.
