Takazudo/zudo-osc-hole-field/circuit/routing/issue189/jl-c2148-reinforcement/README.md

Additive ground-first experiment on the original accepted JL125 input. Artificially separate C2148 only for redundant-ground search; full original native memberships remain mandatory for final acceptance. Full-width plane fanouts produce7objects and direct links25/41objects at0.025/0.0125mm. These are unvalidated candidate reinforcements, not accepted copper.

The signal then finds0paths around all4reinforcements on outer layers, and0paths with either In2 or In3 additionally enabled for the7-object reinforcement. No combined proposal or native adoption is claimed. All completed guarded runs PASS (9s,9s,5s). Initial helper name signal.py shadowed the standard library; renamed protected_signal.py before the successful run. Do not use standard-library module names for helpers.
