Takazudo/zudo-osc-hole-field/circuit/routing/issue189/jr-d7504-ground-screen/README.md

Exact rejected native JR candidate682ad2f... from run37914521455.
R7530.2 andR7505.2 each failed plane fanout at.025mm and.0125mm:no legal via site
inside the12mm frames. GuardPASS(10s),zero proposed copper.
Direct AGND links retain all native groups and use.3mm track/.6mm via/.25mm
clearance,existing allowed layers and.025mm grid. Neither frame yielded any path.
GuardPASS(7s),zero proposed copper. These are finite negative raster experiments;
no further native run and no adoption. Ground dimensions were not weakened.
