Takazudo/zudo-osc-hole-field/circuit/routing/issue189/jl126-nearest-pairs/README.md

Identical accepted JL126 native dump and the same24 nearest disconnected copper
component pairs. Unlike whole-pad spans, frames surround the closest points of
actual native groups; full original group membership is retained in the router
and remains mandatory for native acceptance. Both produce zero paths and no copper.

fine.py:0.025mm raster,weight1,300000expansions/window,guardPASS(85s).
coarse-weighted.py:0.05mm raster,weight2.5,same expansion budget,guardPASS(51s).
This changes two search parameters,so timings do not isolate either effect.
Exact elapsed times,hashes,frames and failure diagnostics are in each JSON.
Native NOT RUN; no canonical board changes. These finite failures are not a proof
of physical impossibility and are not grounds to raise an unchanged search budget.
