Takazudo/zudo-osc-hole-field/circuit/routing/issue189/jl126-ranked-cut-screen/README.md

Target-only screen on the accepted JL126 native dump.17 exact candidate cuts,
0.025mm raster,300000expansions/window,weight2.5,at most2500mm² and100mm per
allocation. Each target retains its original native memberships; victim copper is
removed from the disposable raster only. Victim native memberships/restoration
and all native gates are NOT RUN. All17 searched,zero paths/zero proposed copper;
89.756079seconds,heavy-guardPASS(90seconds). No board changes or adoption.
The wider allocations were exploratory and were not passed to the native repair
stage,whose existing50mm frame limit remains unchanged.
