Takazudo/zudo-osc-hole-field/circuit/routing/issue189/jr131-d7411-in2/README.md

# JR131 D7411 In2 bounded continuation

PR223 merged as16a248fc1dee8a68f416207fa3fd098e4e0d6490 after all-five exact-head checks38026221537 passed. Actual main bytes independently match the full-native JR131 proof:7bb70ac47e12c8bb2e2362d78f7602bdf99c2a69214c68aebeef273b0ce11965. All51402accepted copper objects remain. This proposal starts from that accepted input and changes no board file.

Select one whole XE8DD7DCFD030742EDE49 obligation, D7411.1–U7409.6, using F/In2/B:116segments/3vias,0cuts/moves. The alternative four-layer path has4vias and also uses In3. Selection prefers fewer vias and no In3segments; native plane preservation is NOT inferred. prepare.py checks exact saved screen/router/base hashes and retained copper count. proposal.json SHA256a8c68fc29eba1ed40ba56335734aa5bdb991252f2240d3c5c2139cd882f19dcc. No automatic connectivity restoration or publication is enabled.

The original eight-case screen(PASS40s) was rerun on identical saved input against actual merged board bytes(PASS42s). All8outcomes,diagnostics,paths and proposal geometries are exactly identical; two D7411 domains complete, six trials fail. same-input-comparison.json records per-case timings without a speedup claim. Initial replay attempted the full-adoption dump and stopped at its immutable pilot-input hash before routing. input-equivalence.json proves only the workspace path differs; geometry and every other field are identical. The exact original pilot hash remained enforced on the successful replay.

Local evidence validation passes before/after preparation;19targeted scope/workflow/copper-identity tests pass. Full source regeneration is covered by the passing exact parent CI and must pass on the final source/head in CI. Local pinned KiCad10.0.6 remains unavailable because its image cannot unpack within this cloud filesystem; no substituted oracle or installer retry is used.

Next: run routing-benchmark.yml on this isolated branch with board=osc-jack-right,local_repair=true,local_mode=coupled. This is a read-only native pilot. Require settled baseline/candidate/fresh connectivity, no original group split, zero DRC/parity errors, exact51402old copper retention, zero cuts/moves and unchanged panel/electrical context. Even a positive pilot requires full source-bound capped-warning audits and fresh replay before adoption. Full native result is NOT RUN at this commit. Keep #189 open; no fabrication or hardware qualification.

Reproduce search from artifact11659542859(SHA2569ce87e2b7817faae8b6bbf4c7414214cc373ab58604134ec64a90142880f0f2a): extract the sole suffix osc-jack-right-grid-189-jr133-in3-two-whole-fresh/dump.json, then run replay_screen.py with that path under heavy-guard. Saved dump SHA256a9f1b738f0e541ca5f01d7057f7bb002289e0bf43b90cb223253287f4e5abd84. Run prepare.py from this checkout to reproduce proposal/plan/selection exactly.

## Terminal native rejection

Pilot38028516299/sourcec2634390bca277d6acbb0f5caddff8809e80f57c is rejected: C7523.2/R7331.2 split from original978-pad AGND into976+2. Signal join and AGND split leave131x3→131x3. Independent reconciliationPASS51s verifies all51402old+116segments/3vias,0cuts/moves,1080nonrouting unchanged,0DRC/parity,520raw warnings. Candidateced4240944e5f16ebcf8b3c17ebf29347a2fe57c920530aa31c5fa39c0786230. Artifact11661282364 SHA256957703181f52e69f22bd64f417722024645b8997d86346ac6ec990eb13485f03,19759750bytes. No fresh stage or complete warning audits followed rejection; neither passed. Main remainsJR131. native-rejection.json and reconcile_pilot.py preserve the exact evidence. Do not adopt or redispatch this unchanged geometry.
