Takazudo/zudo-osc-hole-field/circuit/routing/issue189/core1402-plane-budget/README.md

# Explicit bounded plane-fanout search budget

Plane fanout has one search window. The shared first-window optimization capped it at300,000 expansions regardless of a larger global max_expansions; unlike signal routing, it never reached a second window. The saved U4231.7/J900249.2/C4248.2 control demonstrates requested5,000,000 still reporting actual300,000. This is a search-control limitation, not native connectivity acceptance.

route() and CLI now expose plane_max_expansions/--plane-max-expansions. Default300,000 remains; the global maximum still bounds it. Signal attempt budgets and all physical/electrical/native acceptance rules remain unchanged. Four regressions failed before implementation;42plane/router/obstacle tests pass afterward. Tests cover actual A* arguments and diagnostics, global/default caps, unchanged signal attempts, and invalid budgets.

Same saved accepted core1402 dump5218becd38f6bb612f9a169230bd8e6657776a09fc12af5baa6113825e671ffb and publishedfa60b4e1587a67501782fb55374f0e5d5133f65cd0bbe62624aef502441fda10:3/6mmfanout windows,.0125grid,full0.3mmground/0.6via/.25clearance,original -12Vguard and groups. Default300,000 results match exactly. Explicit5,000,000 now reaches actual limits and exhausts at432,733states(3mm) and445,329states(6mm),instead of being capped at300,001. No route/copper/connectivity gain. Guarded old controlPASS73s,new controlPASS64s; no speedup claim. Full output and comparison hashes retained.

No board/spec/generated output changes. This task starts from verified main16a248fc; local pinnedKiCad10.0.6/aggregate regeneration remains unavailable because the image cannot unpack within this environment's32GBfilesystem, previously verified twice. Do not reinstall/reconfigureDocker or substituteKiCad9. Exact-head remoteCI must cover regeneration and all nativeboardgates. circuit:check is the manual68-line offline inventory check, not schematic/placement binding or hardware qualification. No proposal is eligible for native adoption from this negative screen. Sole coreworker38023611361 remains untouched; any future candidate requires terminal reconciliation and exact accepted-output rebase. Keep189OPEN.

CLI smoke passed with explicitplane5,000,000/global7:both obligations remain unrouted,zero cuts/copper. circuit:checkPASS after retrying the exact command with supported escalation for pnpm's home-store SQLite access; first sandboxed attempt failed before validation. No auth/config changes. No component inventory or generated documentation changed.
