Takazudo/zudo-osc-hole-field/circuit/routing/issue189/core1441-next-no-via/README.md

# Next core no-via screen

Completed 48 cases across the next24 eligible native signal nets, F.Cu and B.Cu separately. 8 positive cases, 105 proposed objects. Elapsed 296.53588395200495s; heavy guard PASS299s. These are raster proposals only, not native joins or accepted copper. Original core1441 input; the active core26 worker remains the sole writer.
