Takazudo/zudo-osc-hole-field/circuit/routing/issue189/core1441-third-no-via/README.md

# Third core no-via screen

Completed 48 cases across the next24 eligible native signal nets after the previous48, F.Cu and B.Cu separately. 6 positive cases, 92 proposed objects. Elapsed 344.34764423900924s; heavy guardPASS349s. Original core1441 input. These are raster proposals only, not native joins or accepted copper. The active core26 worker remains the sole writer.
