Takazudo/zudo-osc-hole-field/circuit/routing/issue189/jr-d7504-outer-avoid/README.md

UNREBASED; NATIVE NOT RUN. This changed D7504 alternative uses outer layers only and one via at(411.4,176.35), with9objects,zero removals. The previous34-object/two-via native candidate preserved R7505 but split R7530; this is a new geometry, not an accepted repair.

Wait for JR37925027262 to finish, inspect its actual receipt/artifact and reconcile accepted copper. Then run:

.circuit-cache/route-venv/bin/python circuit/routing/issue189/jr-d7504-outer-avoid/rebase_proposal.py --accepted-sha256 ACTUAL_PUBLISHED_SHA256

The helper requires every prior full copper block unchanged, allows only the known233-object pending delta or no change, rejects UUID and clearance conflicts, and fails closed on any unexpected subset. Inspect generated plan/rebase before adding workflow choice d7504-outer-avoid and dispatching exactly one JR writer. Full native gates remain mandatory.

## Terminal native result

Run37927714132 completed successfully but rejected the candidate:141→142 (one signal join, two AGND splits atR7505.2/R7530.2), zero DRC/parity errors,520 unchanged warnings, fresh connectivity agrees. All50964 accepted objects were retained exactly and nine added. Canonical JR remains141. Artifact11614927392 ZIP SHA2564ae076bd0682327fd4dafc3d088640ab9cfc87dd01611710f060506990db3d7f verified; candidate/replay hashes and pad details in native-result.json. Worker receipt-only commit598d64bf63338270d8d79e07b6a57e0fc29a9d2f was cherry-picked without modifying any board. Do not rerun the unchanged nine-object proposal.
