Takazudo/zudo-osc-hole-field/circuit/routing/issue189/jr-three-remaining/README.md

UNREBASED; NATIVE NOT RUN. Three additive signal transactions,233objects,zero removals,from actual native JR141. They are geometrically mutually compatible and clear of pending34-object D7504 output; see jr141-remaining-short/gaps.json. The39- and139-object alternatives conflict with pending D7504 and are excluded. D7208 is held aside because of prior nearby supply-split evidence; no native equivalence is assumed.

After sole JR37923452631 is terminal, inspect its actual receipt/native artifact and reconcile accepted copper. Then run:

.circuit-cache/route-venv/bin/python circuit/routing/issue189/jr-three-remaining/rebase_proposal.py --accepted-sha256 ACTUAL_PUBLISHED_SHA256

The helper permits only the known pending34-object delta or no change, preserves every prior full copper block including legacy duplicate IDs, and rejects UUID/gap conflicts. Inspect the generated plan/rebase before adding workflow choice three-remaining and submitting exactly one JR writer. Full original-baseline native connectivity, DRC/parity, warning, settled-fill and fresh checks remain mandatory.
