Takazudo/zudo-osc-hole-field/circuit/routing/issue189/core1441-next24/README.md

Next24 previously untried open signal nets on the immutable accepted1441 native
dump.0.025mm raster,300000expansions/window,existing signal dimensions/layers and
fill guard.2paths/32objects in199seconds;guardPASS(200s). Exact elapsed time and
hashes inprobe.json. OneR4249.2 path is a single segment; C2304.1 path has31objects.
All proposals NATIVE NOTRUN and bound to old1441 published input. Rebase and verify
all retained copper after the sole core writer finishes; never overwrite its
accepted geometry. Do not mix these with pending supplies without conflict checks.
