Takazudo/zudo-osc-hole-field/schematic/exports/master-hierarchy.pdf

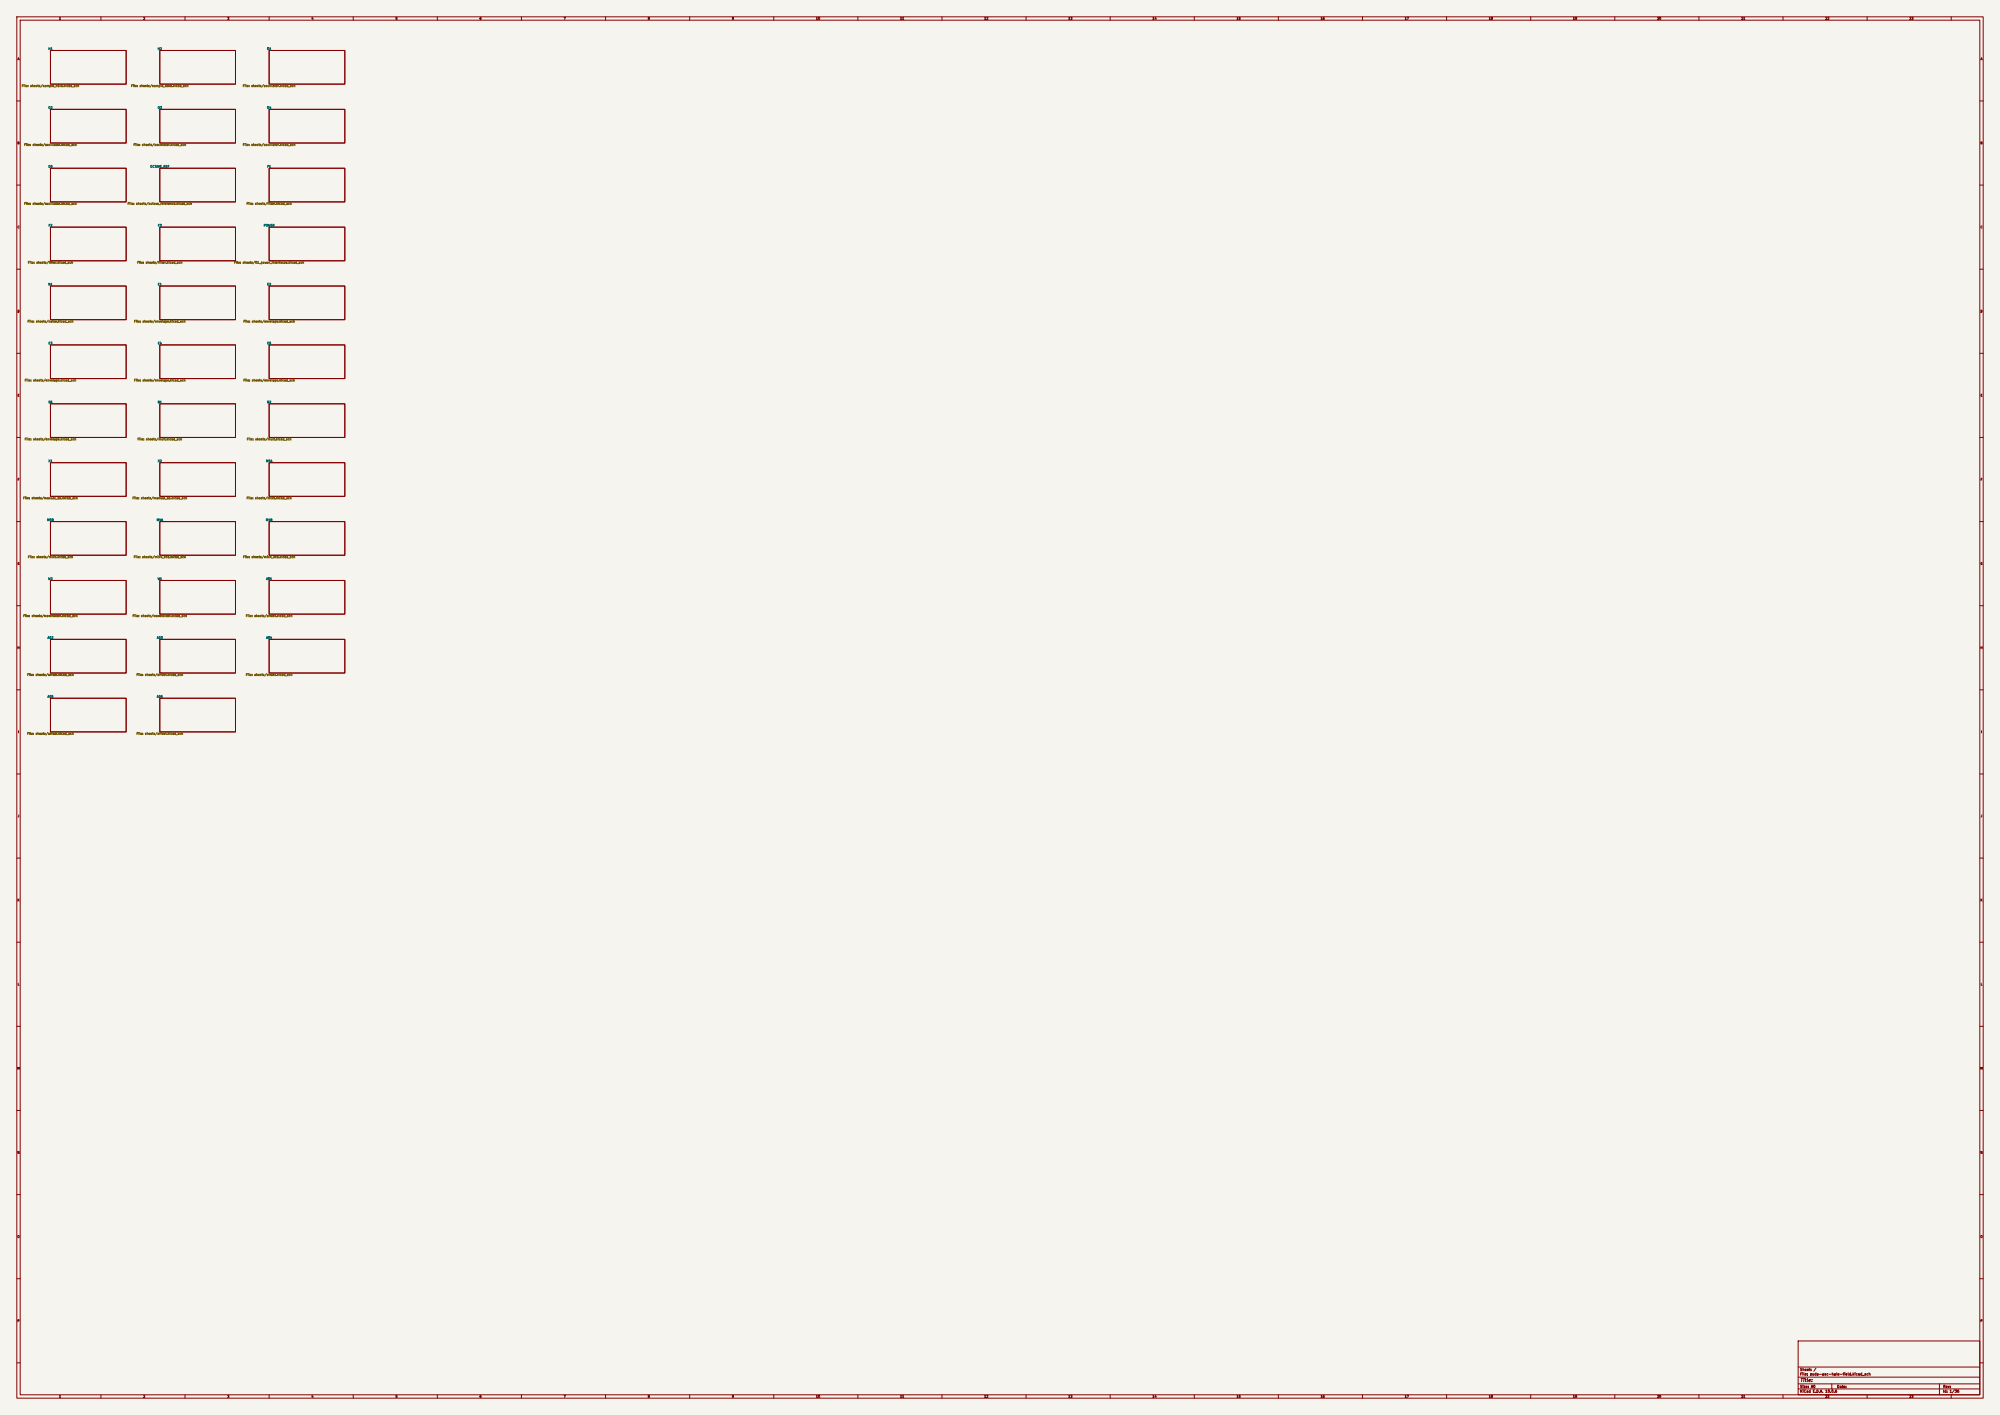
[picture p44: page 1]

Sheet: /
File: zudo-osc-hole-field.kicad_sch
Title:

Size: A0 | Rev:
KiCad E.D.A. 10.0.6 | Id: 1/36

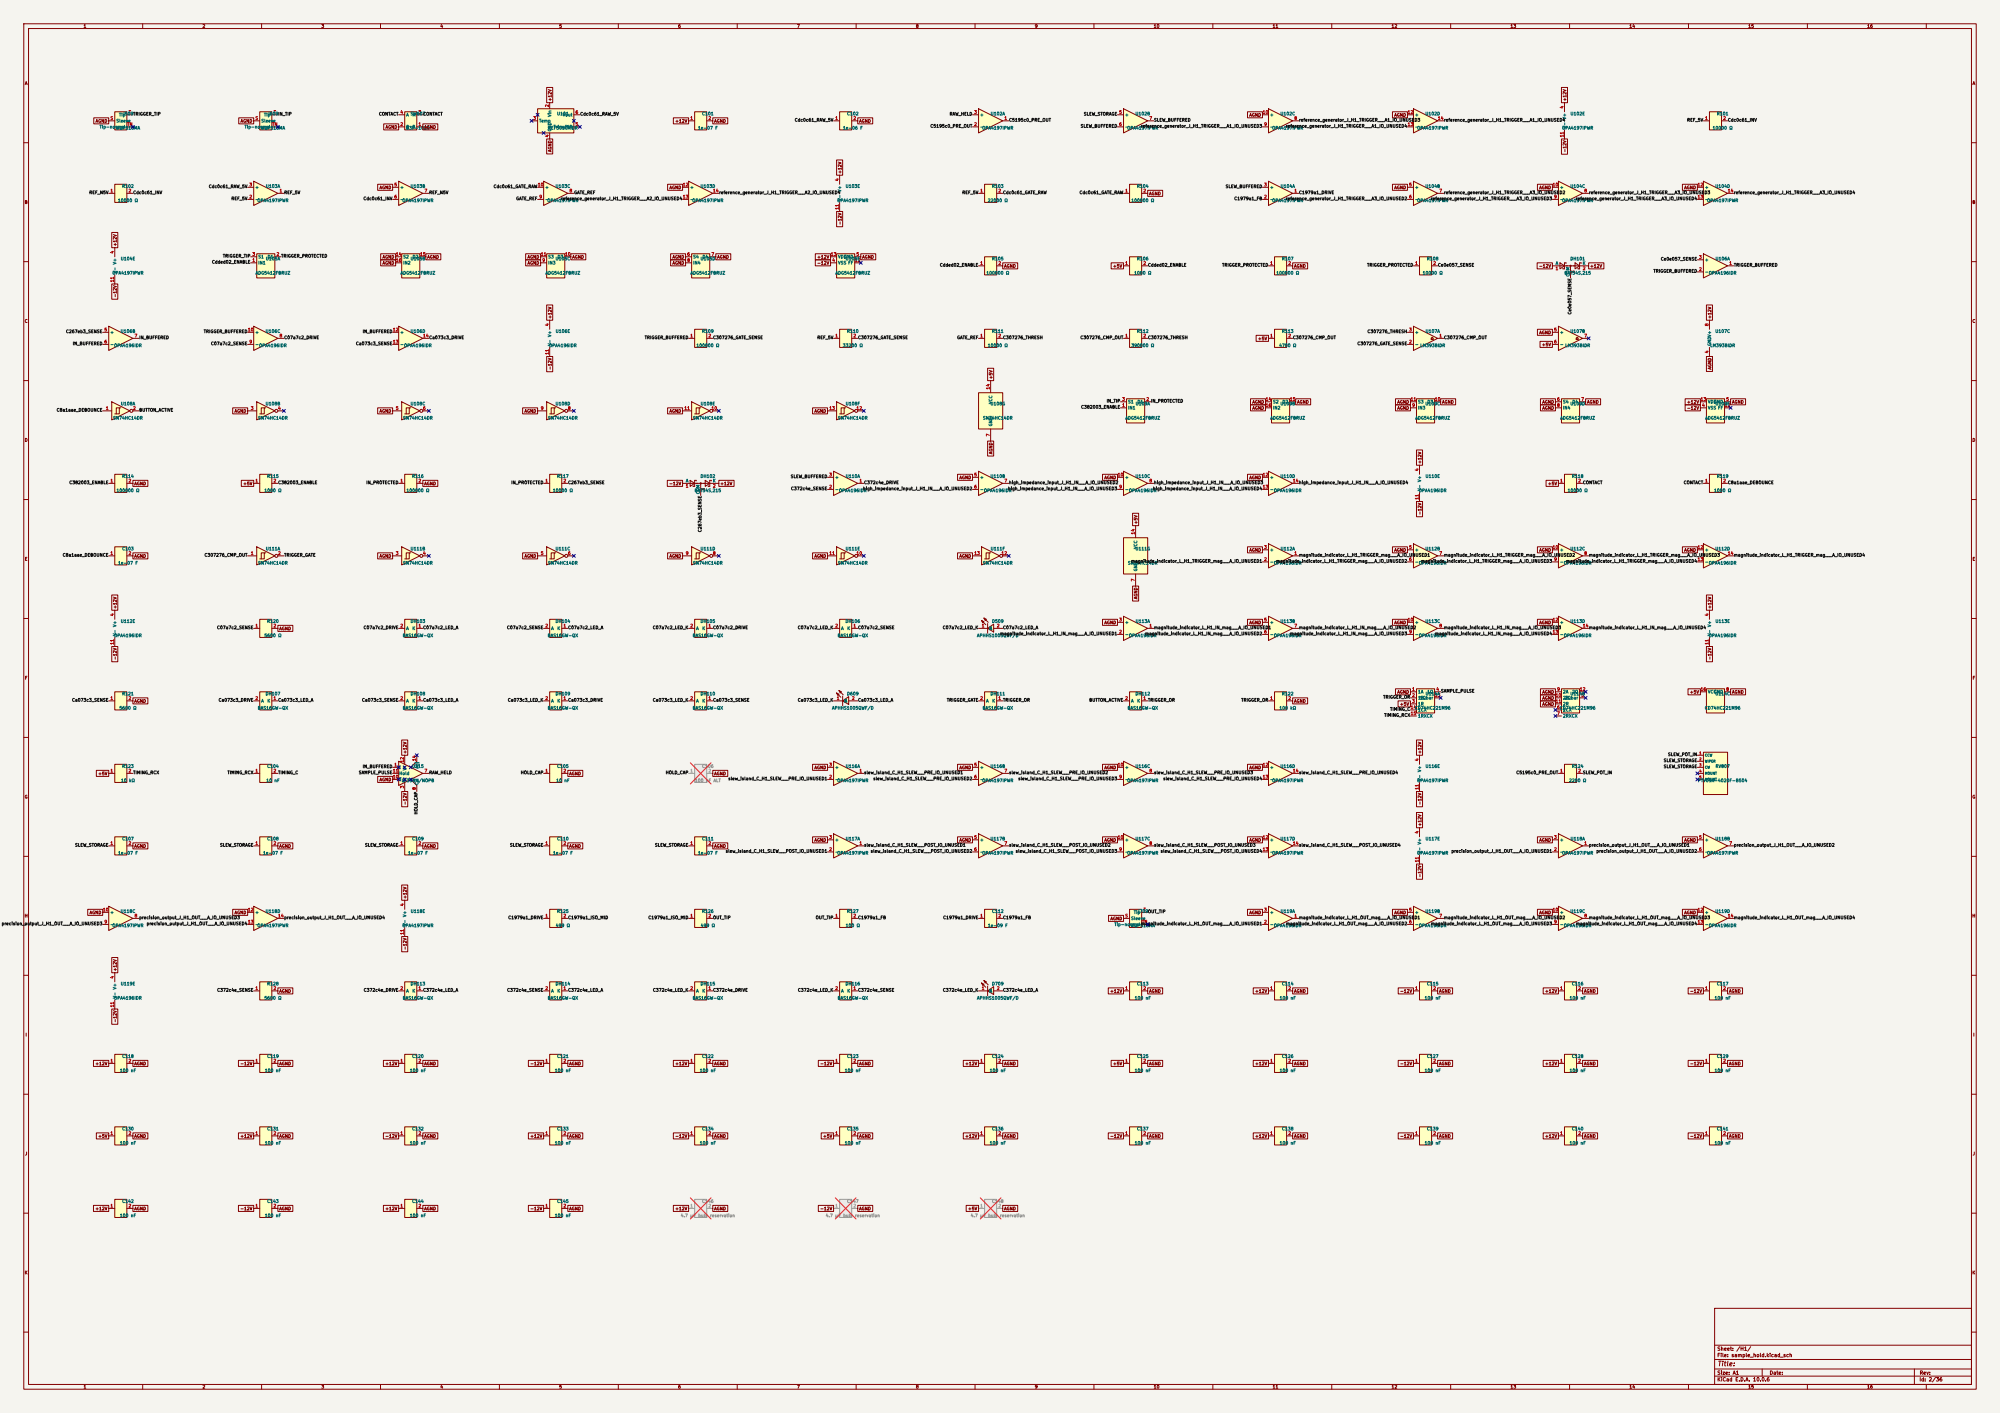
[picture p45: page 2]

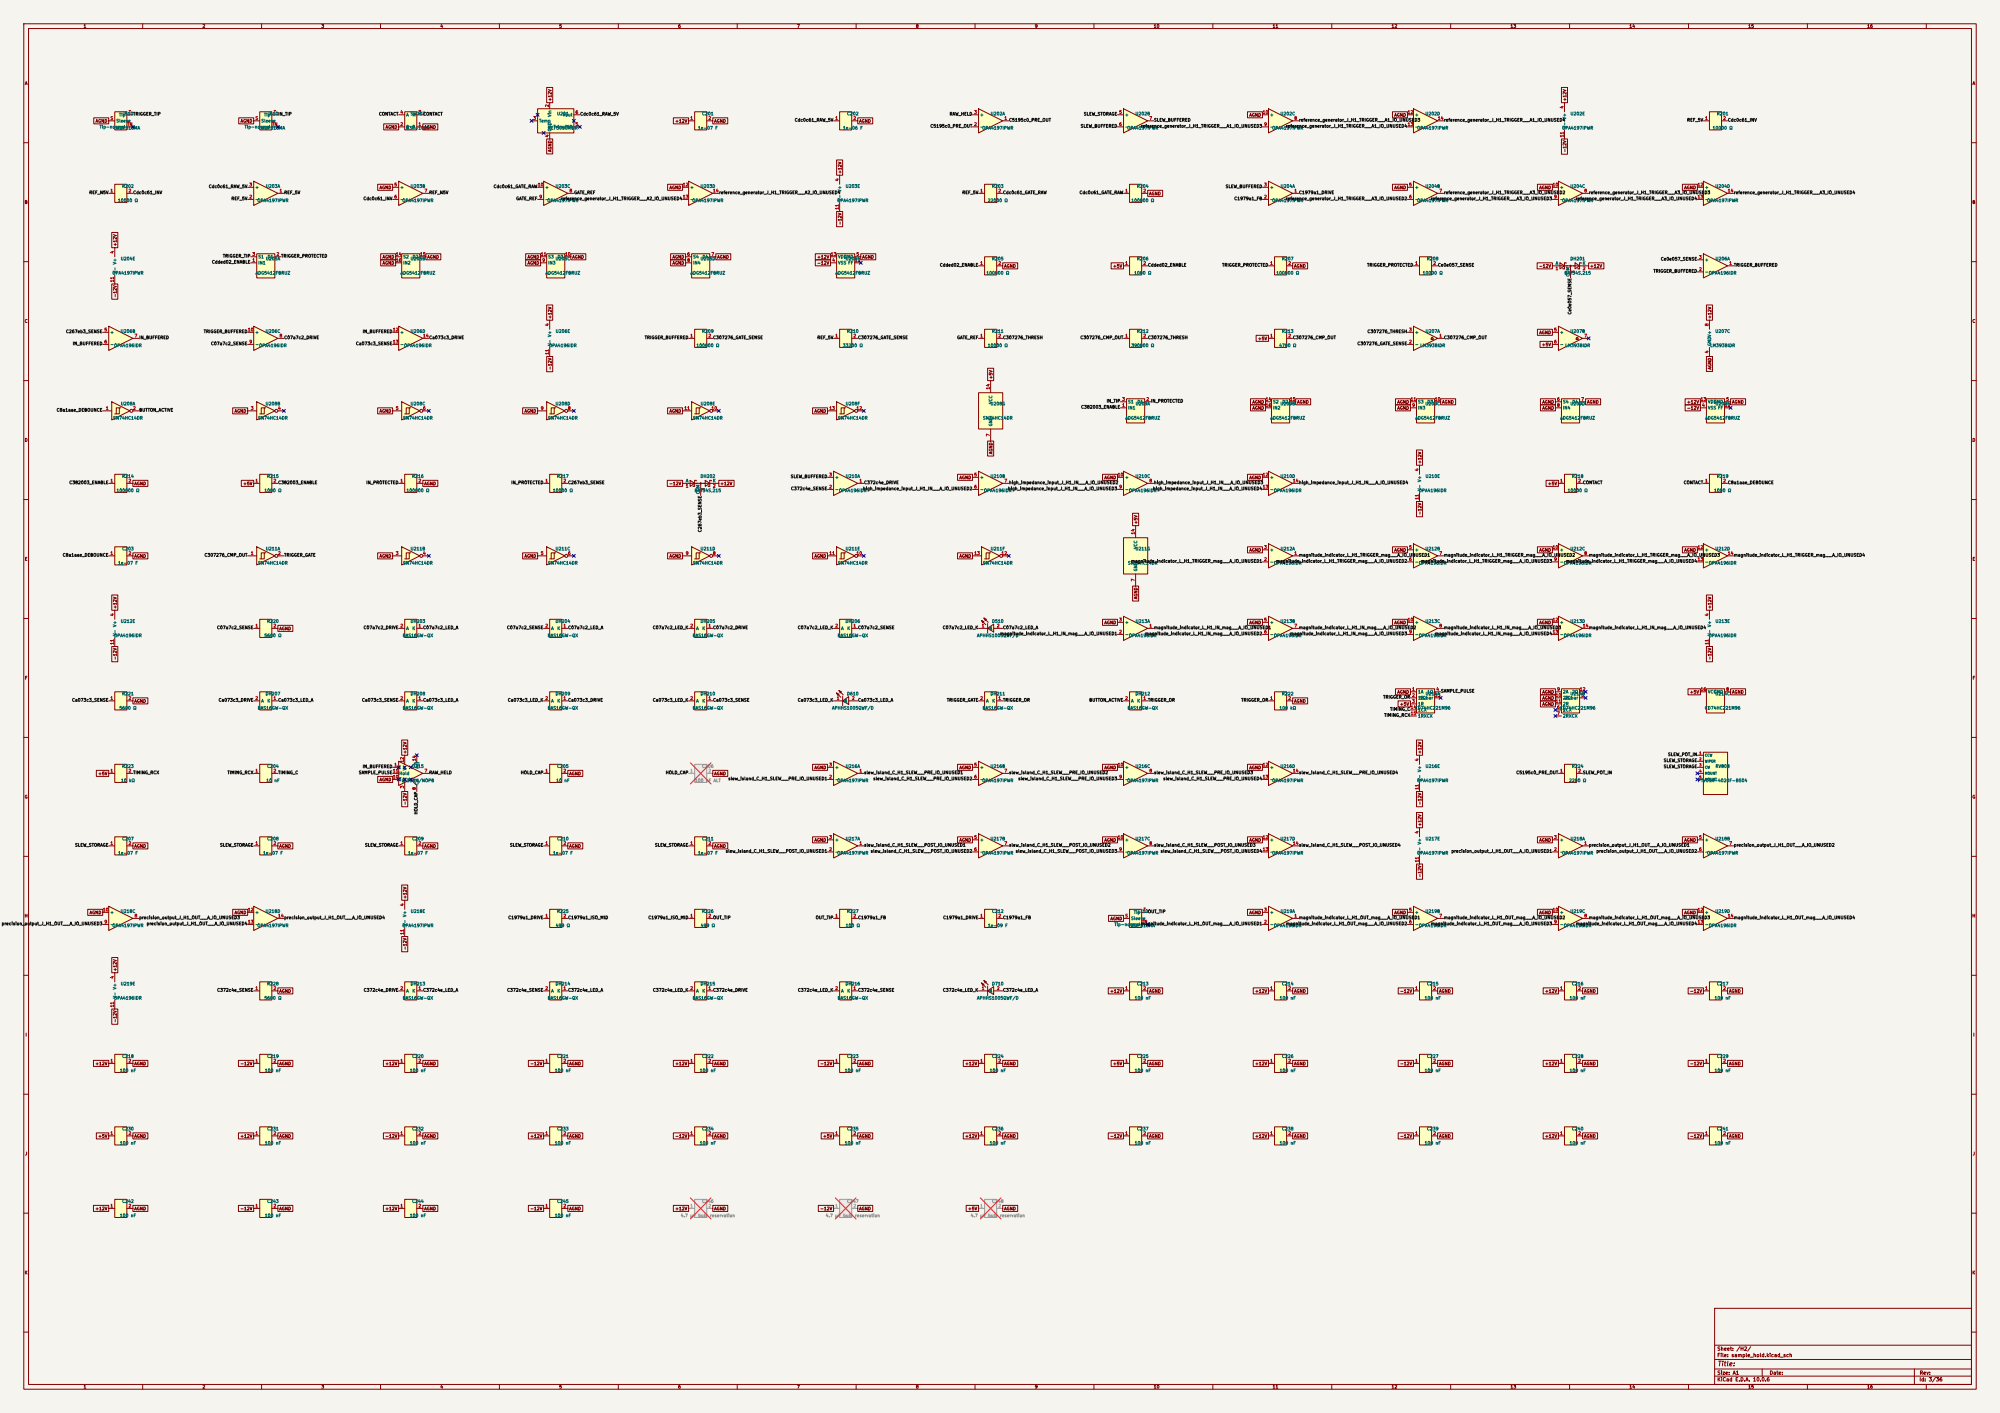
[picture p46: page 3]

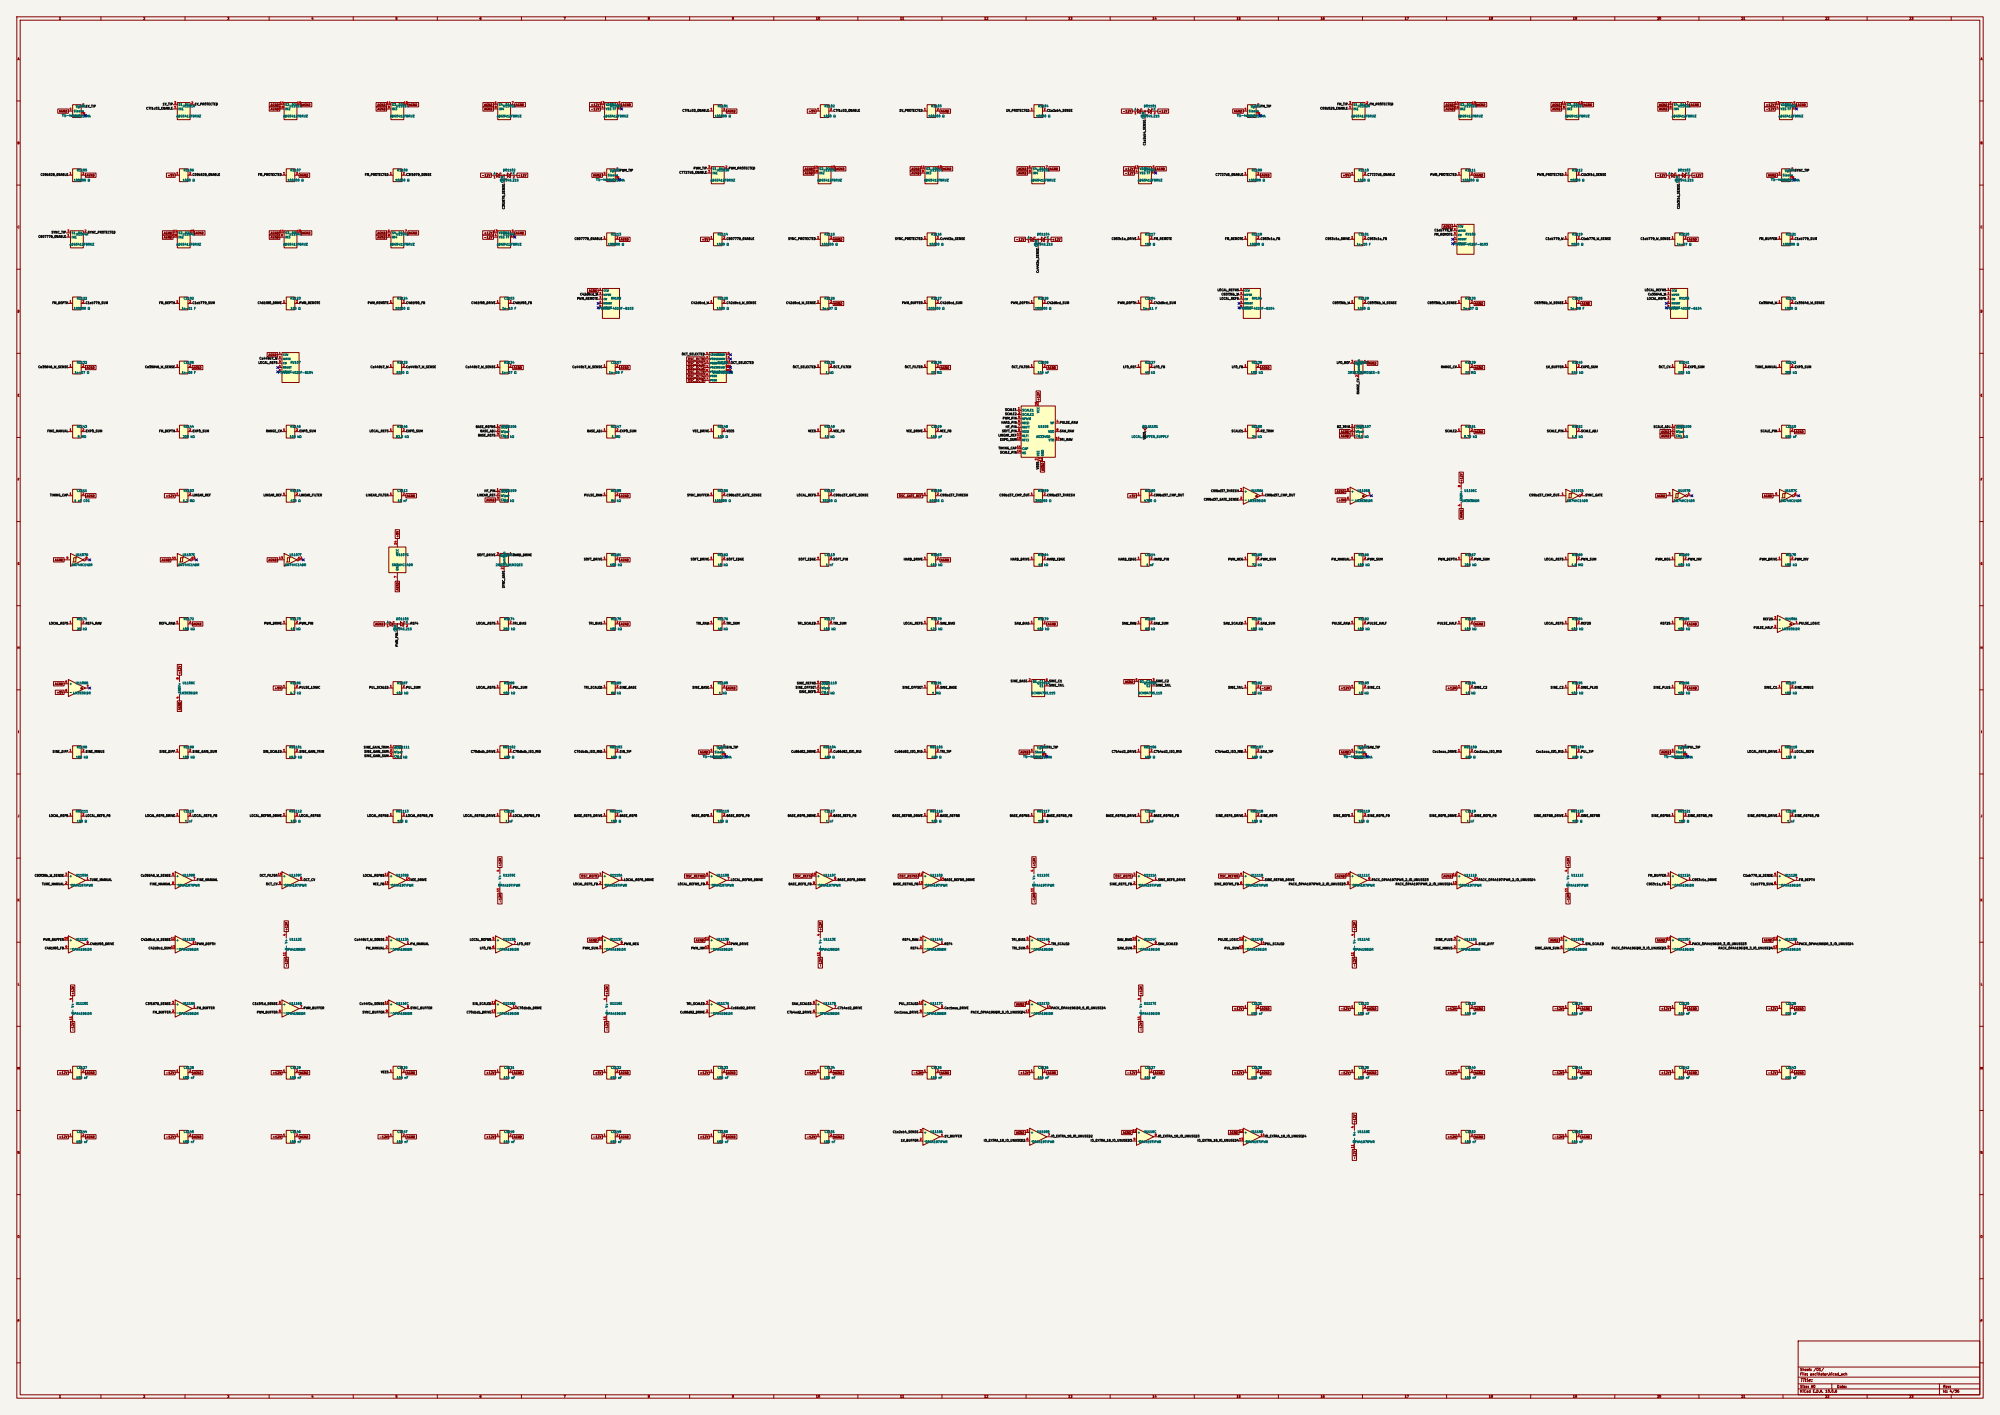
[picture p47: page 4]

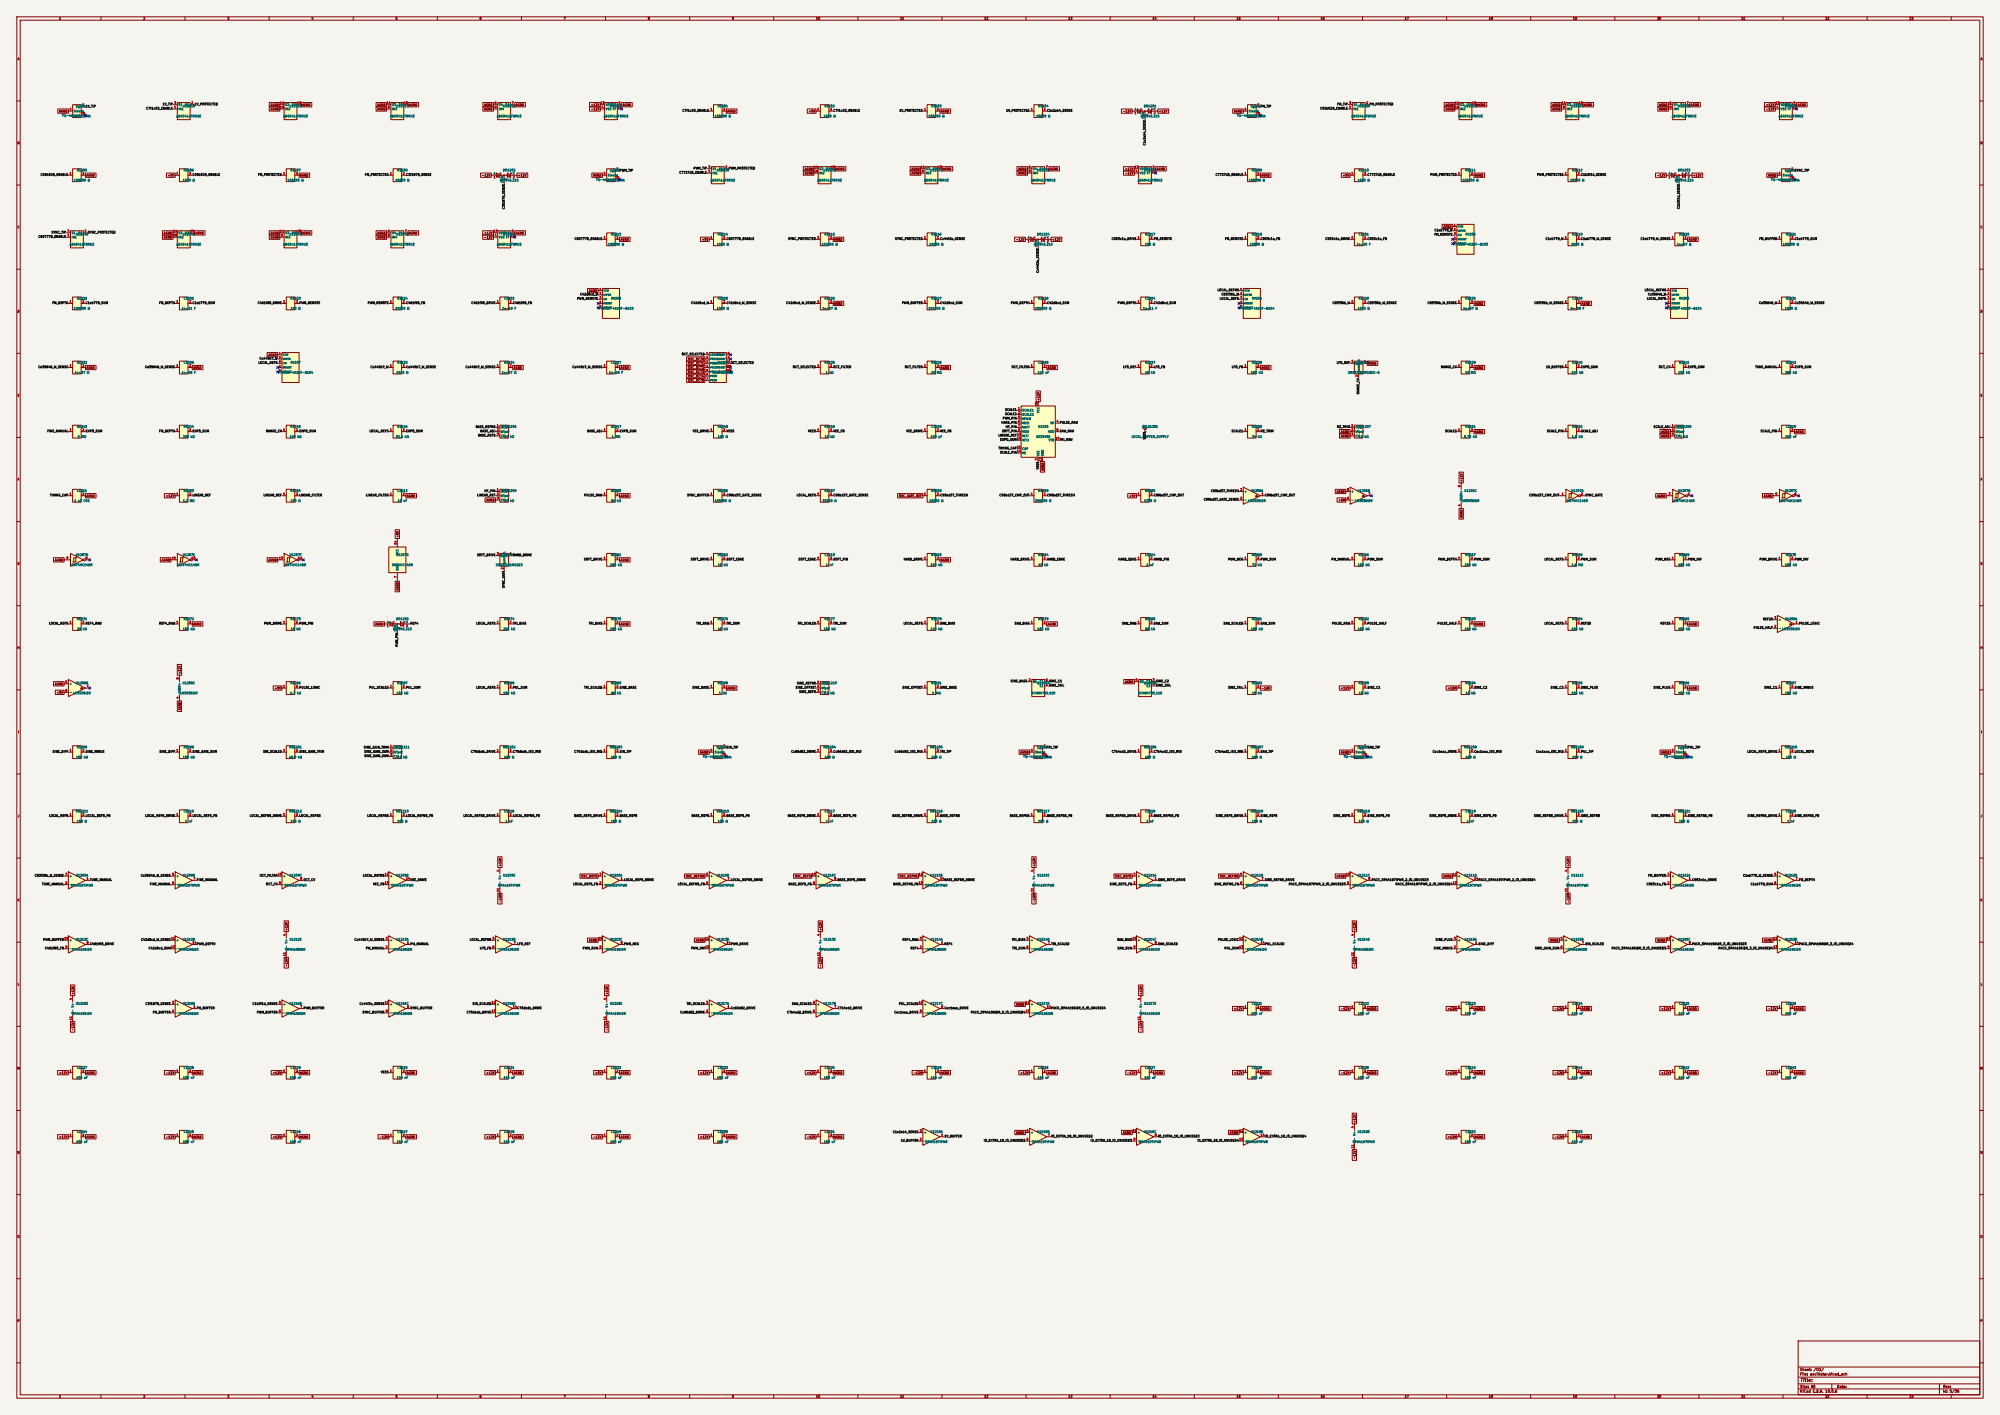
[picture p48: page 5]

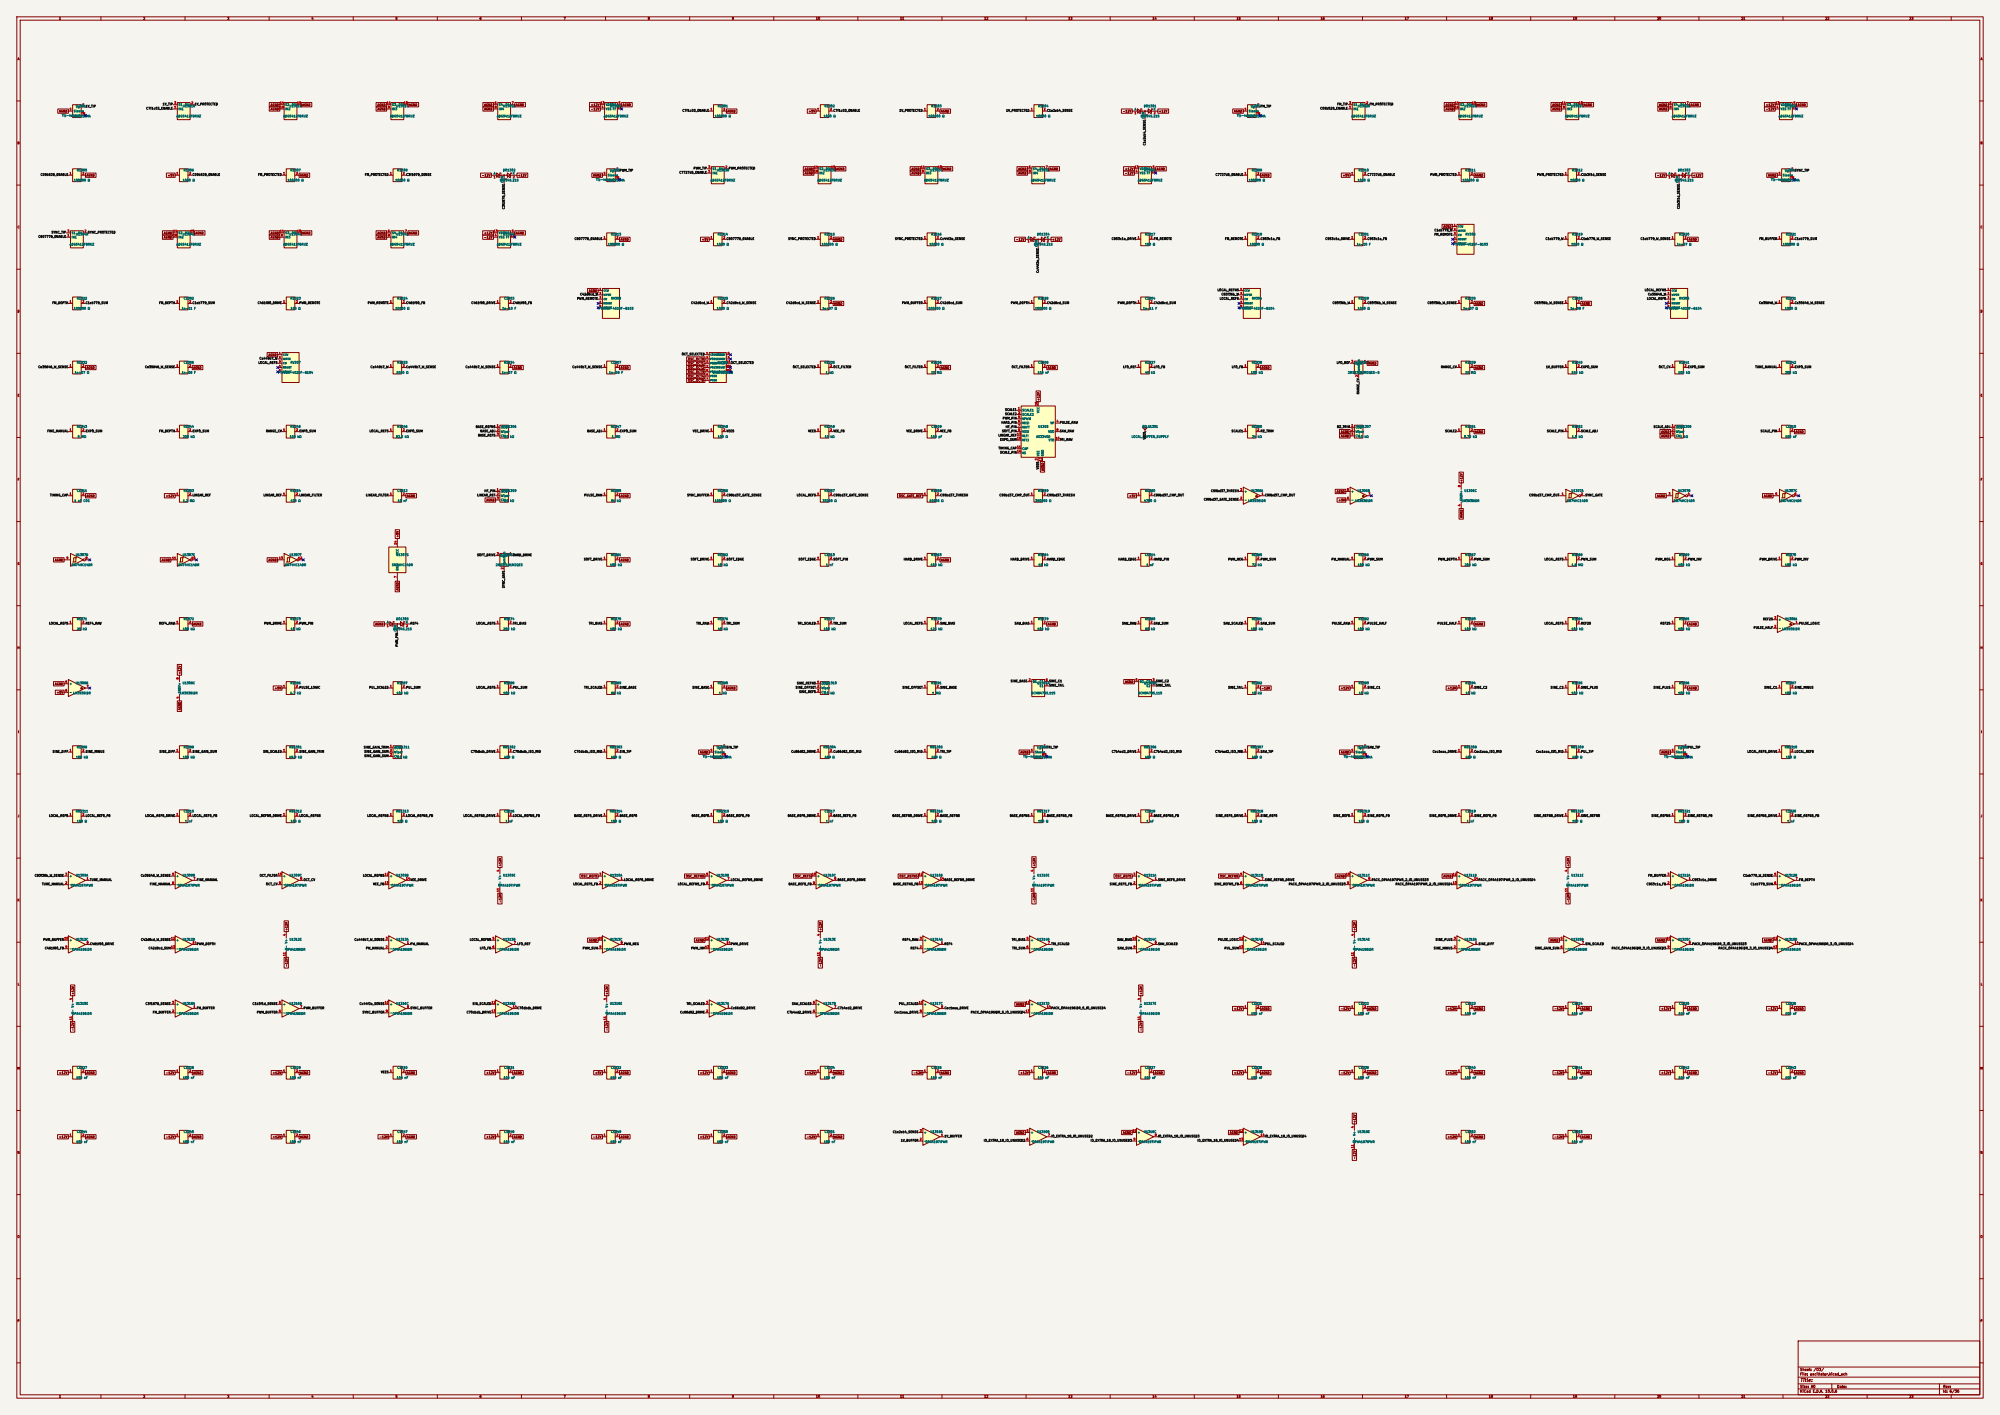
[picture p49: page 6]

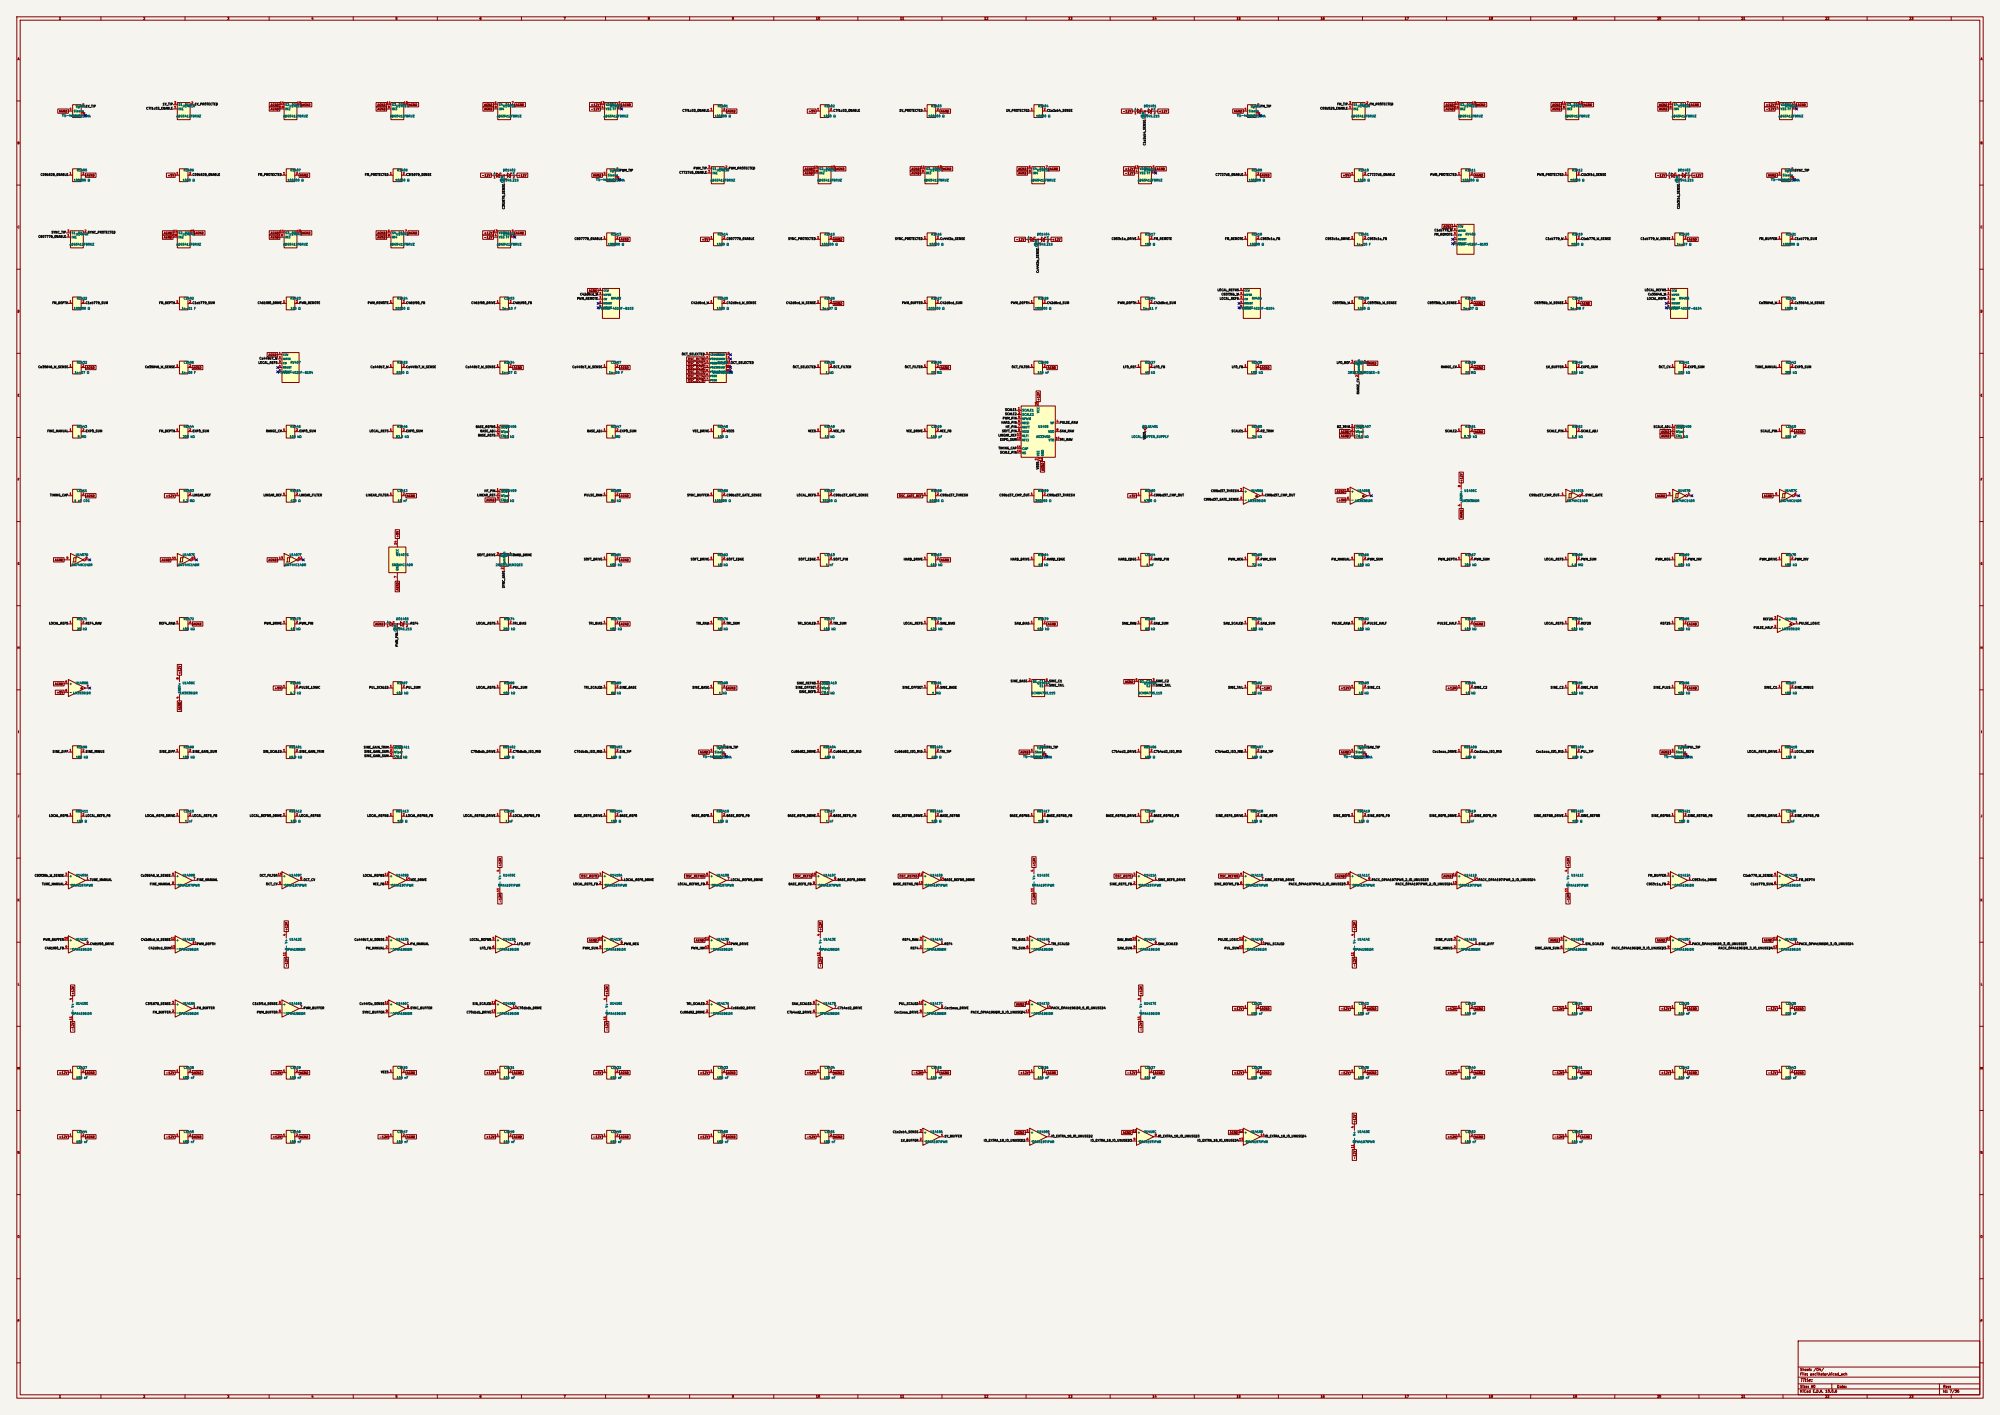
[picture p50: page 7]

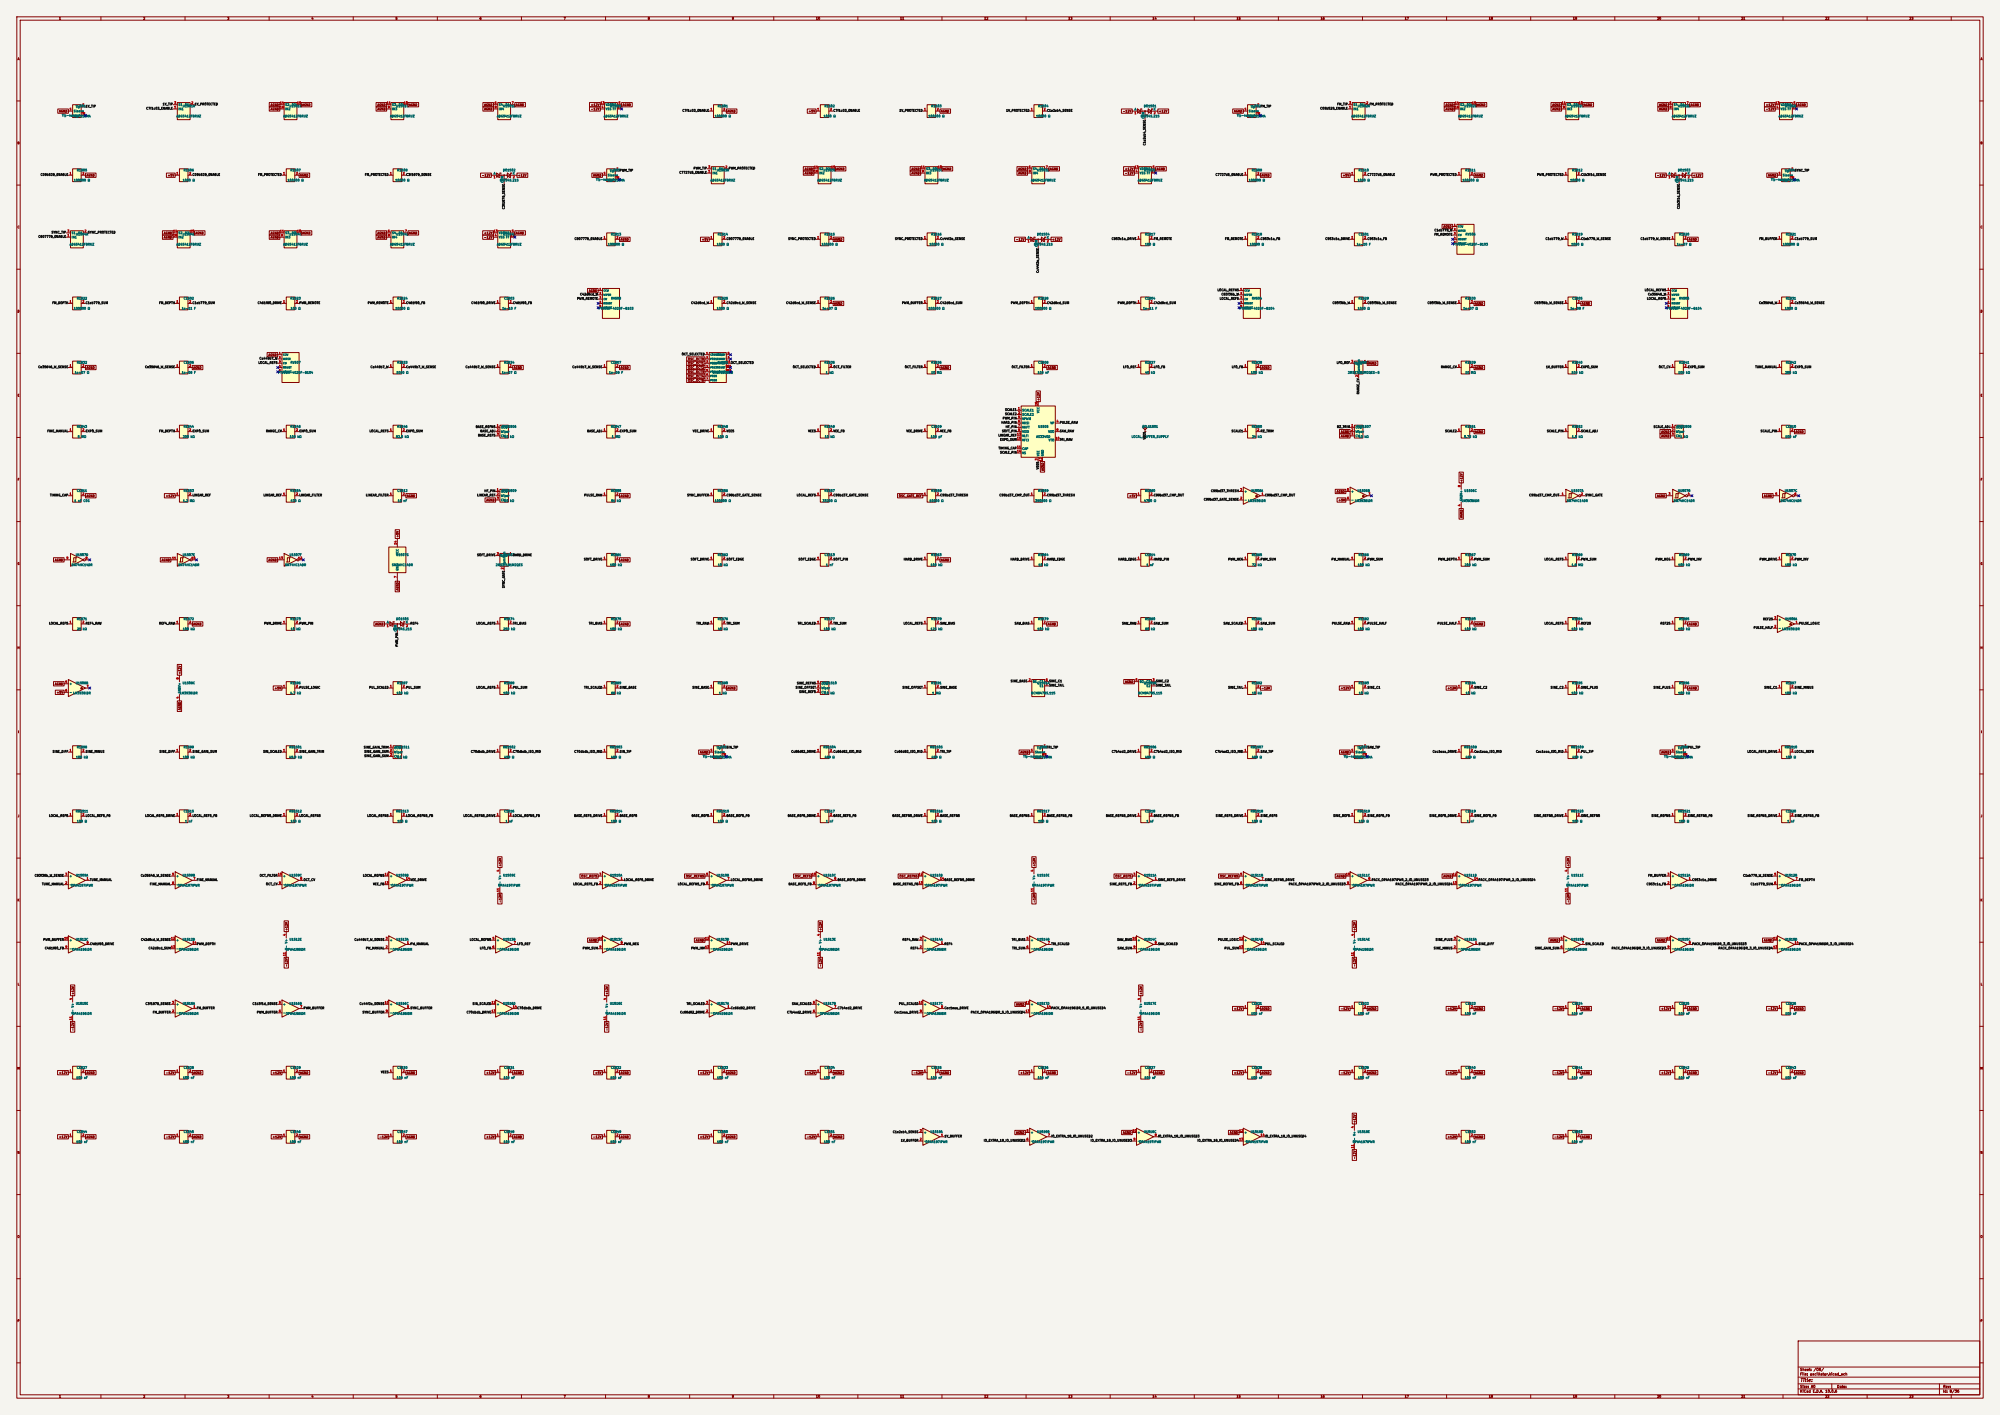
[picture p51: page 8]

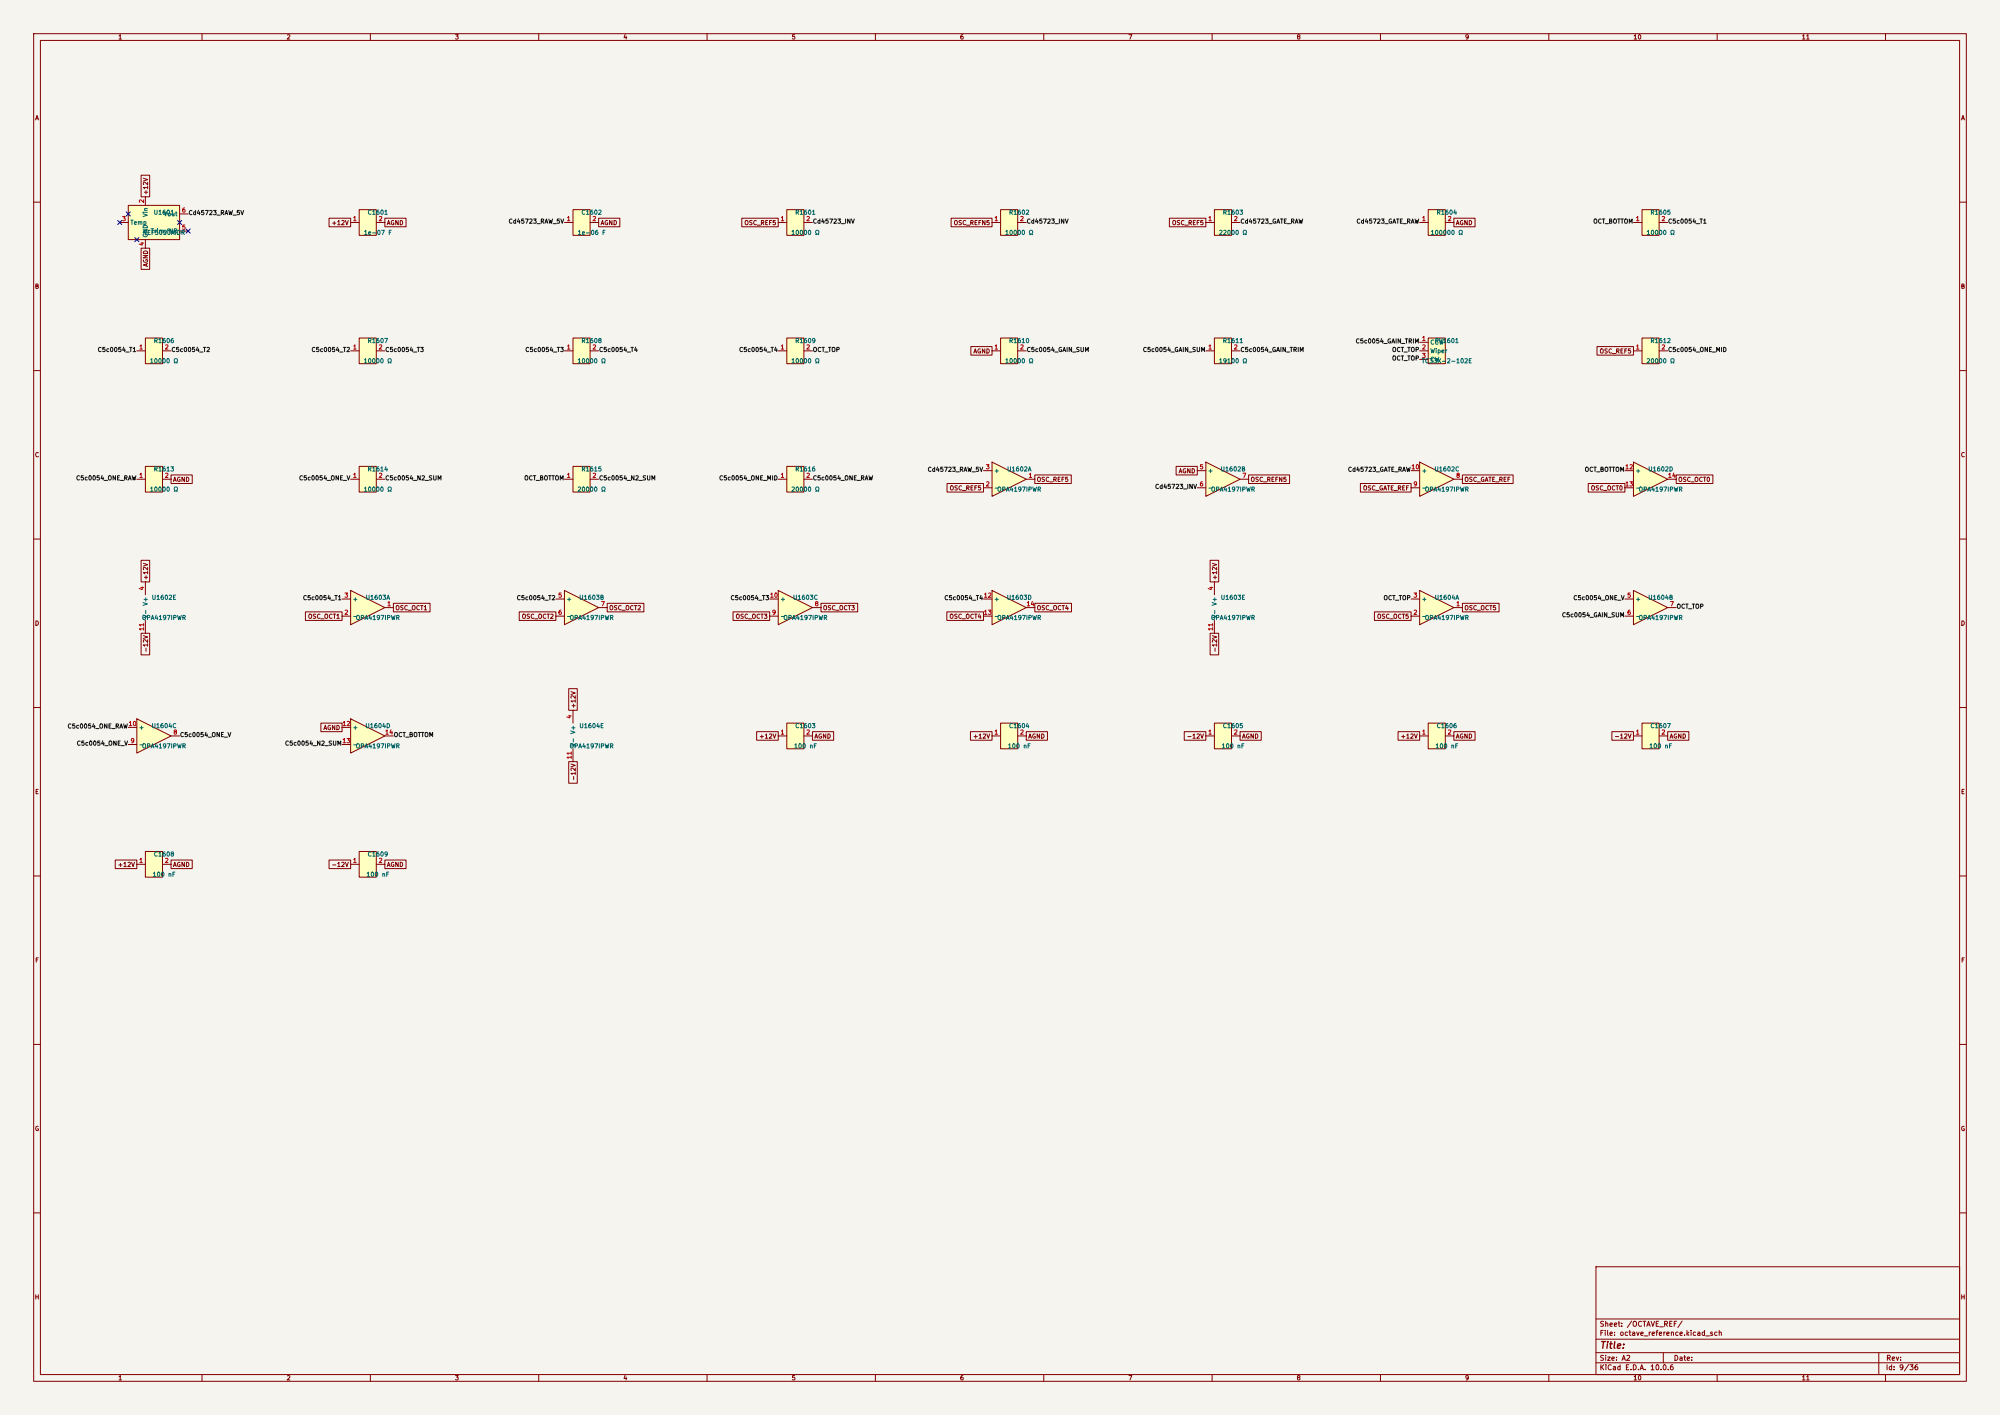
[picture p52: page 9]

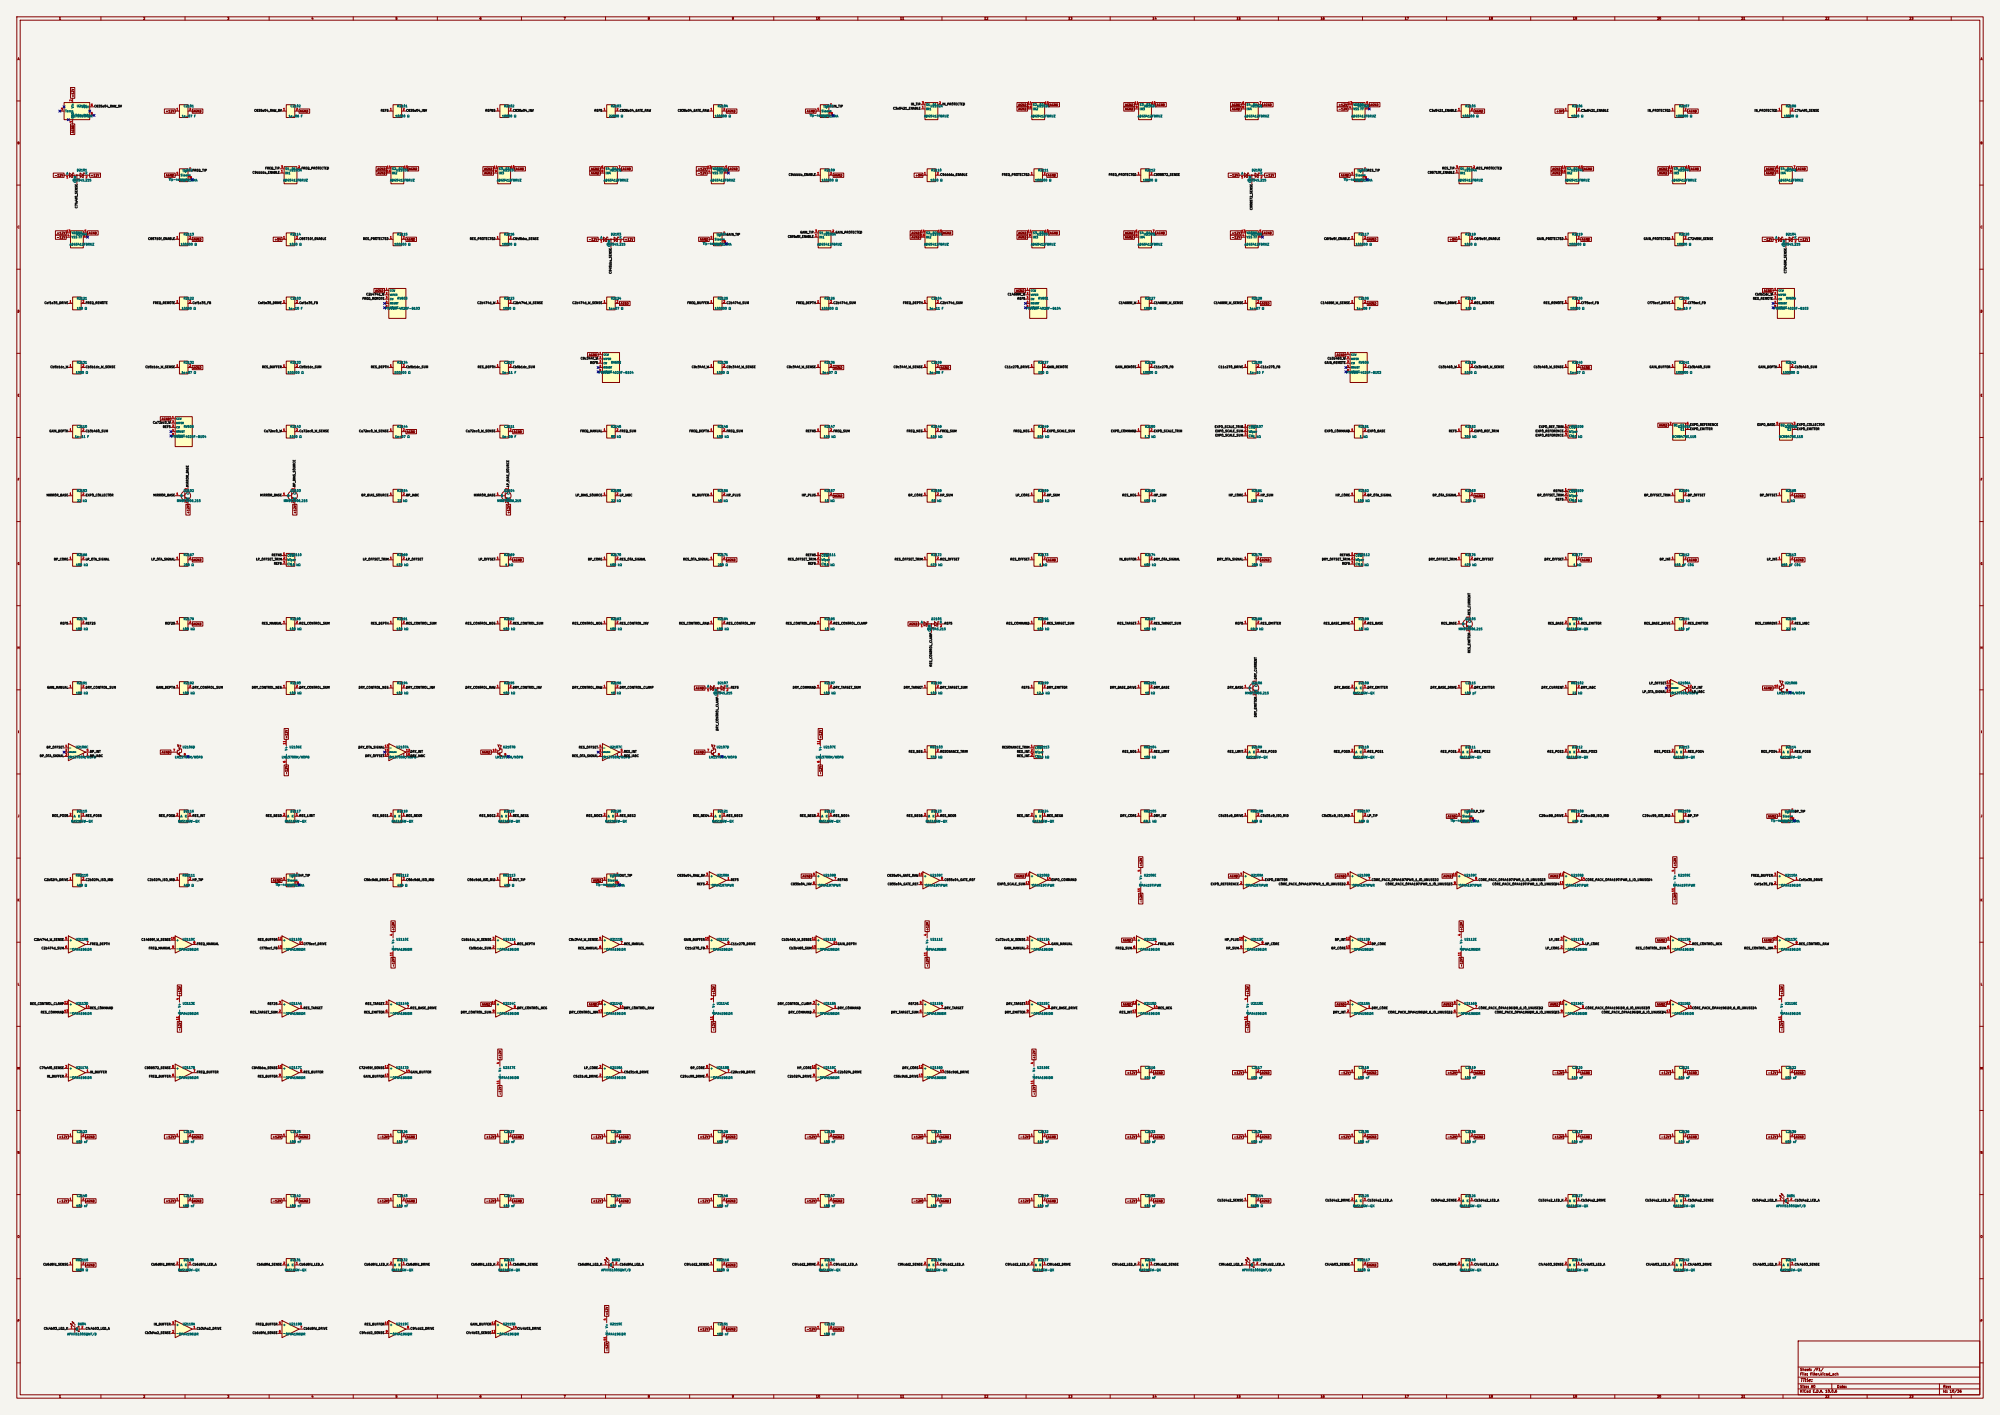
[picture p53: page 10]

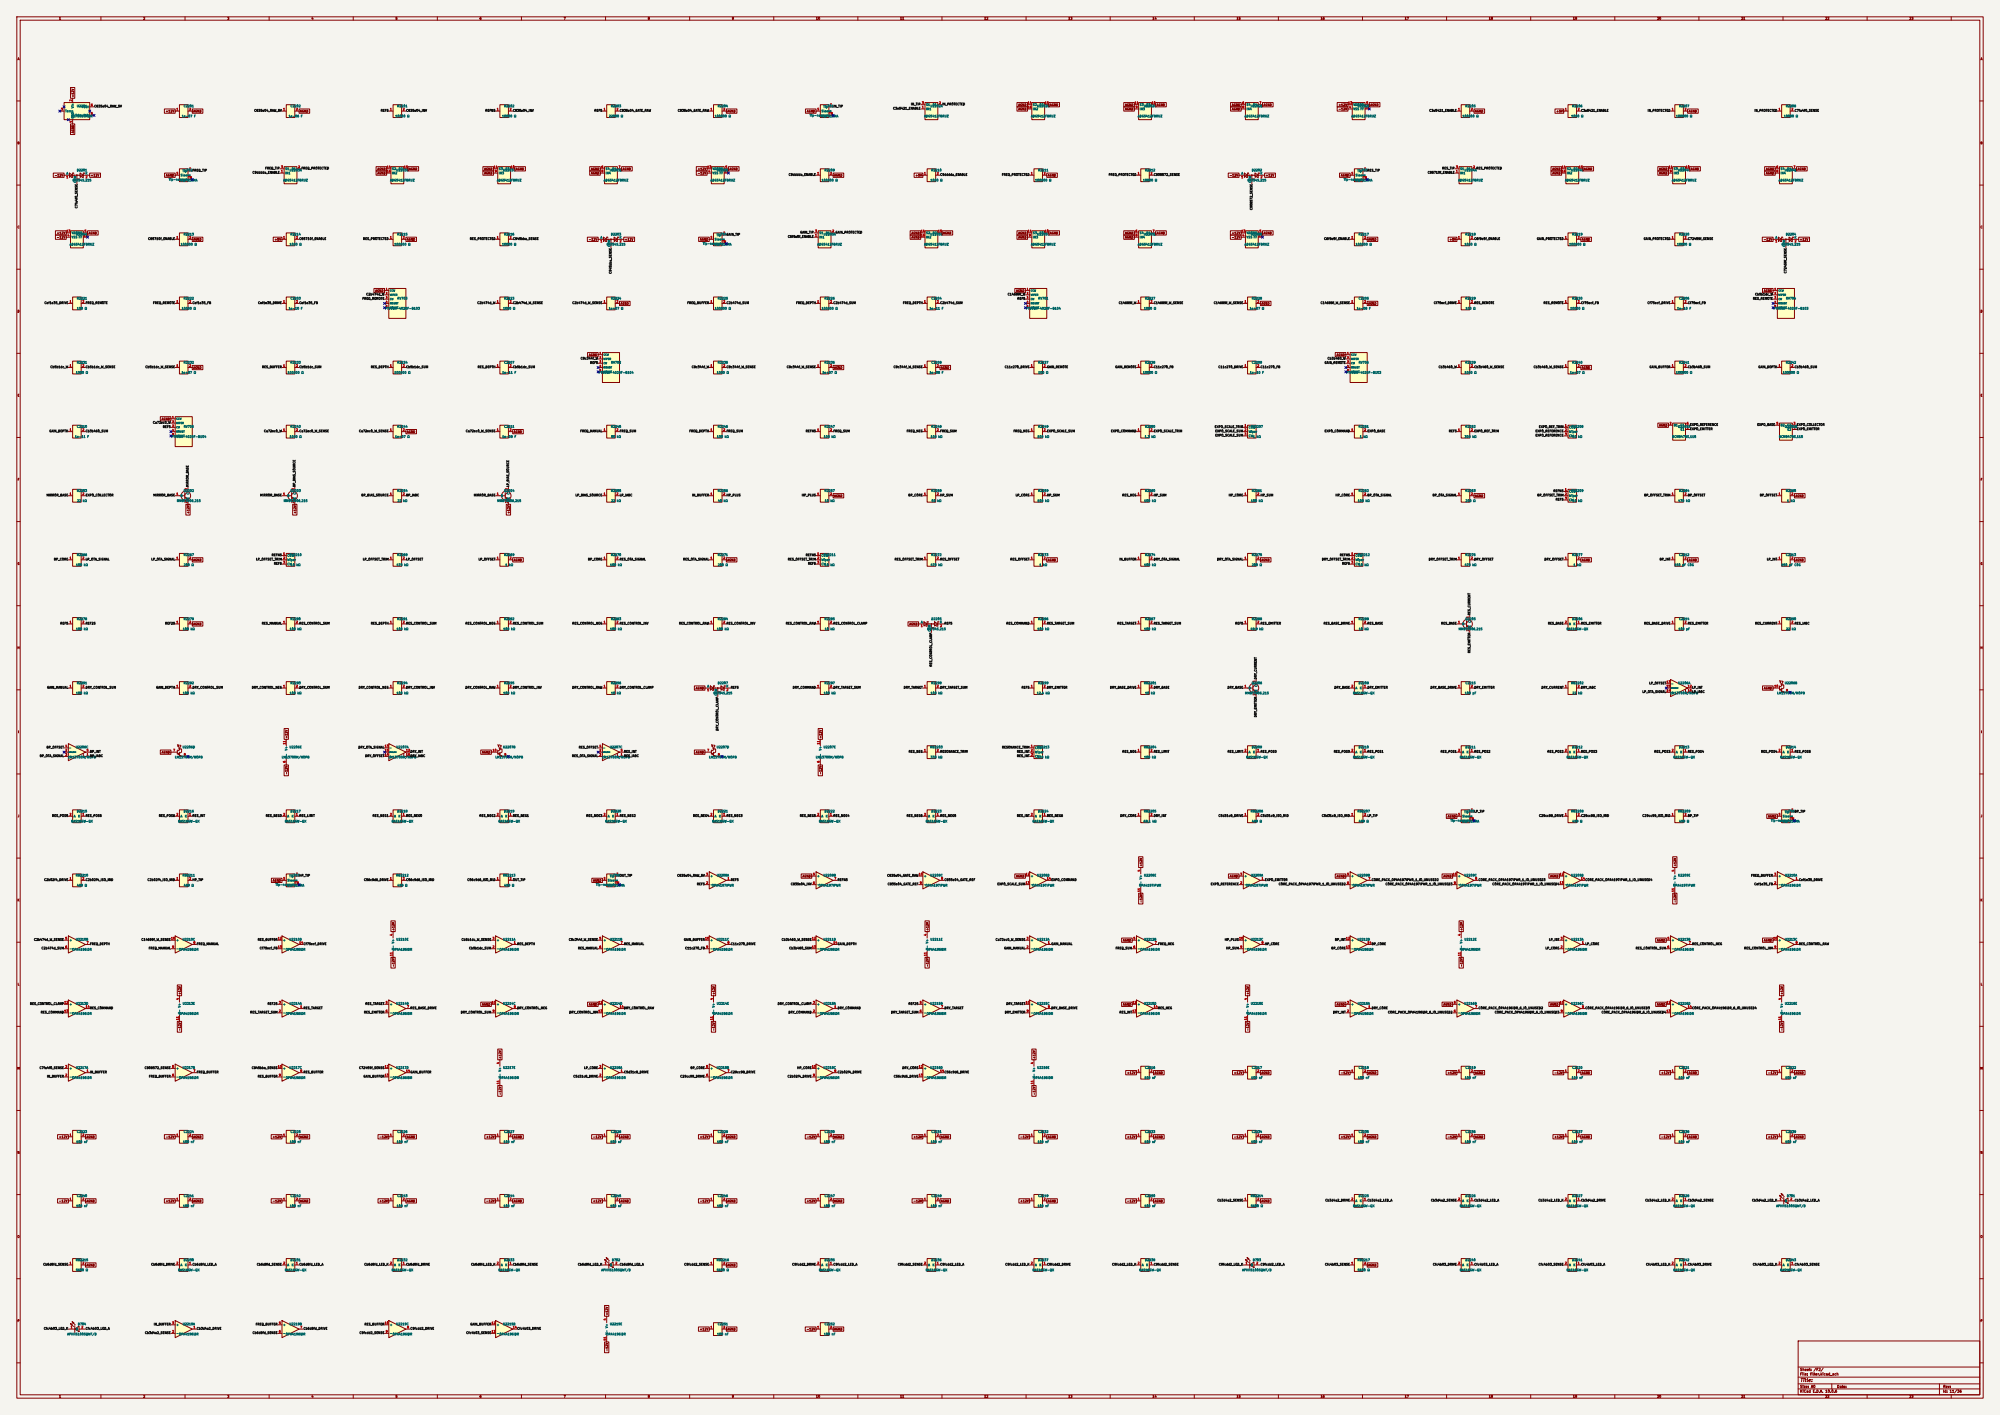
[picture p54: page 11]

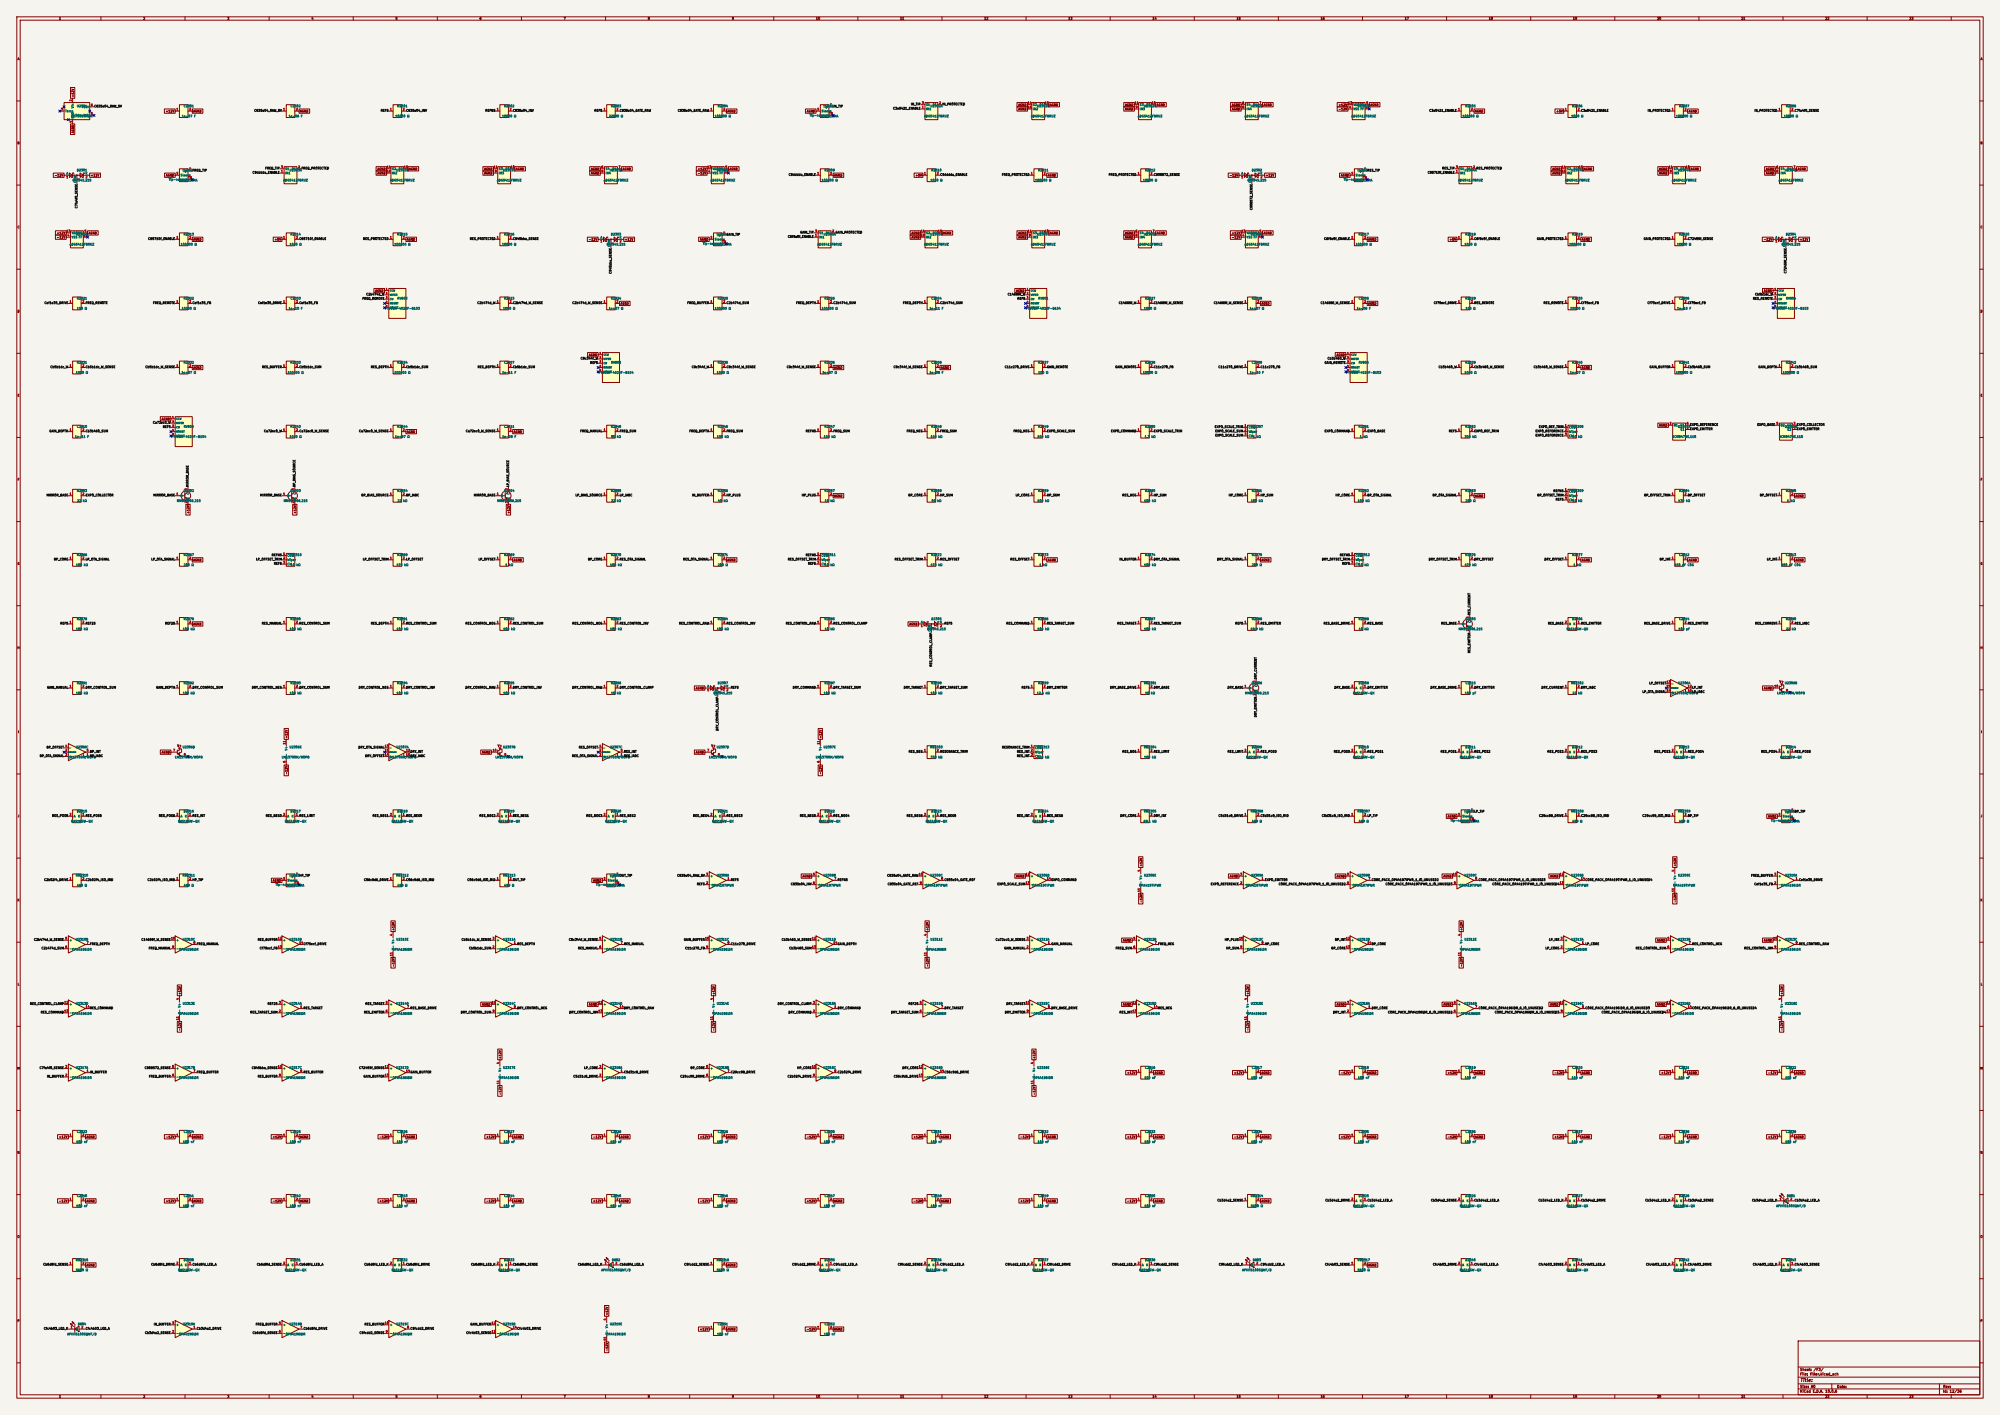
[picture p55: page 12]

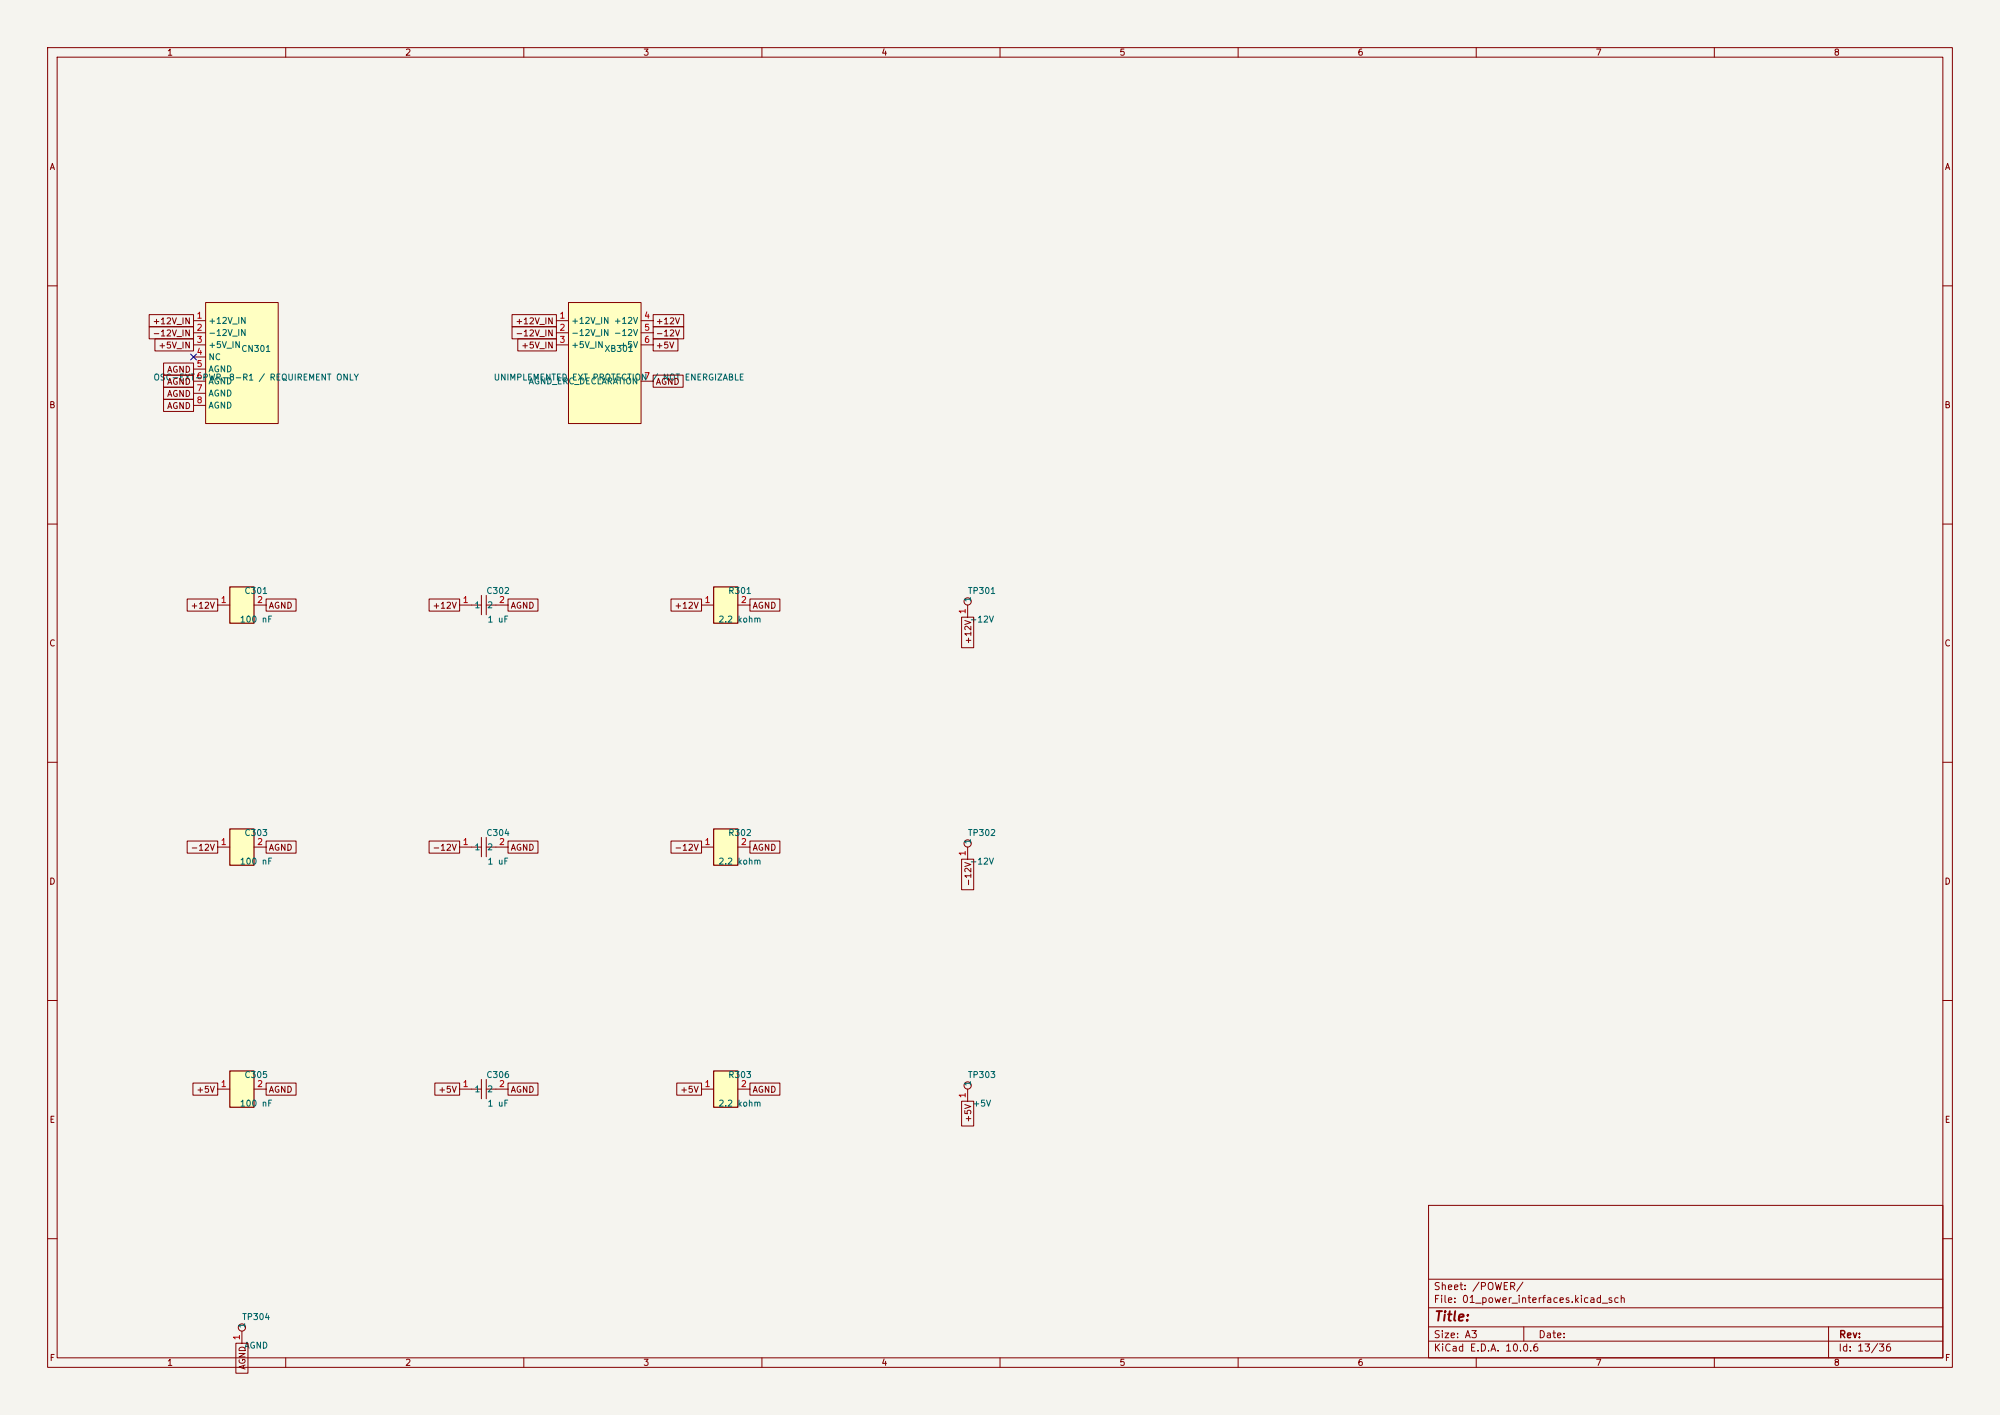
[picture p56: page 13]

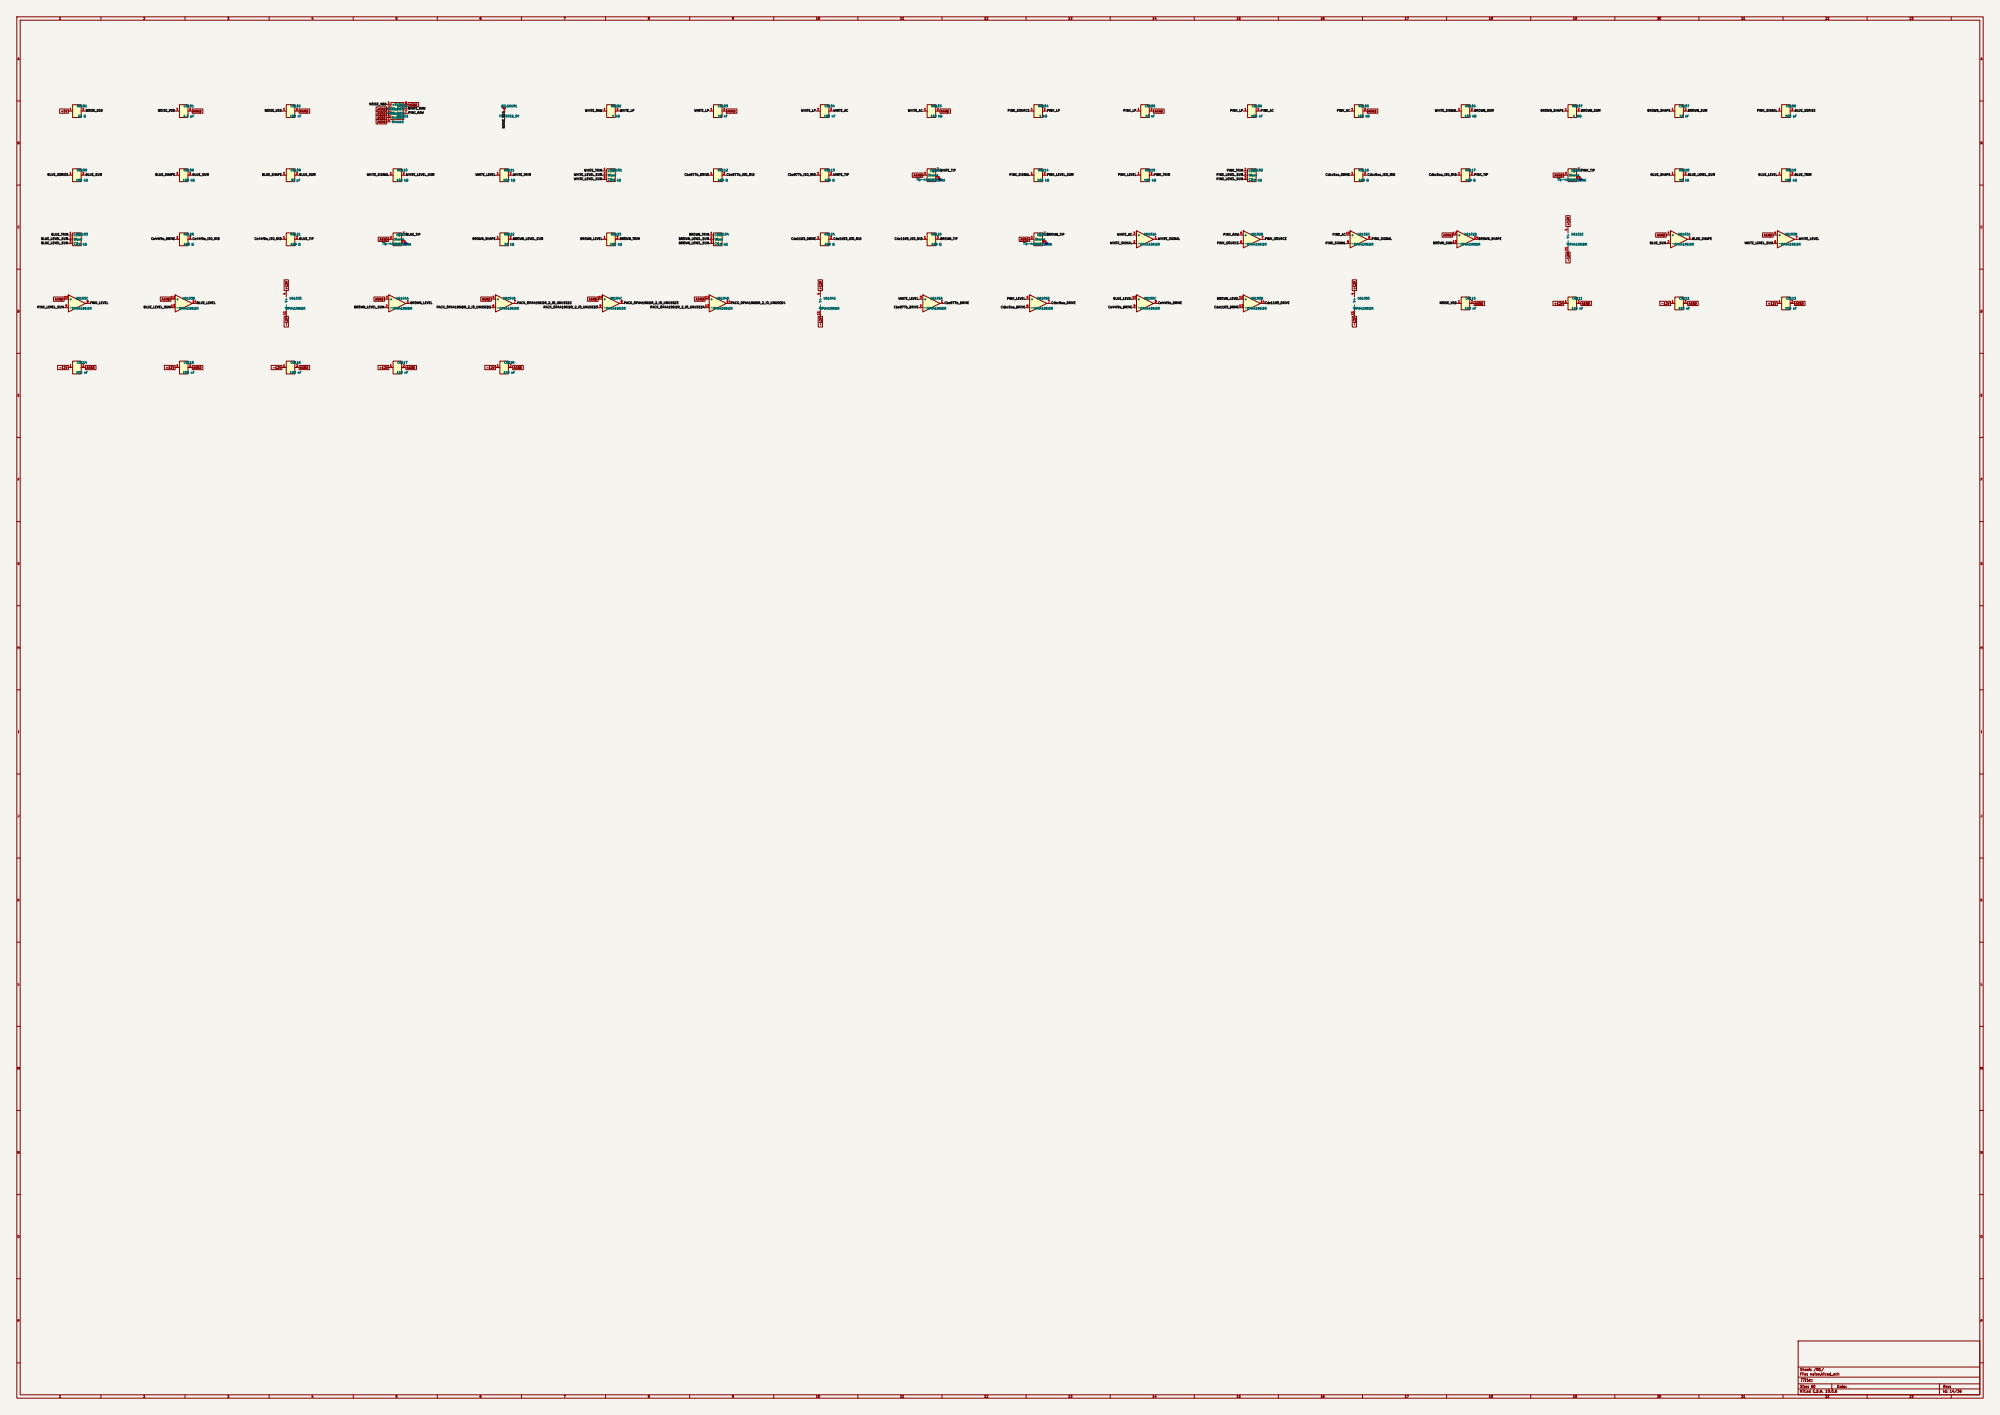
[picture p57: page 14]

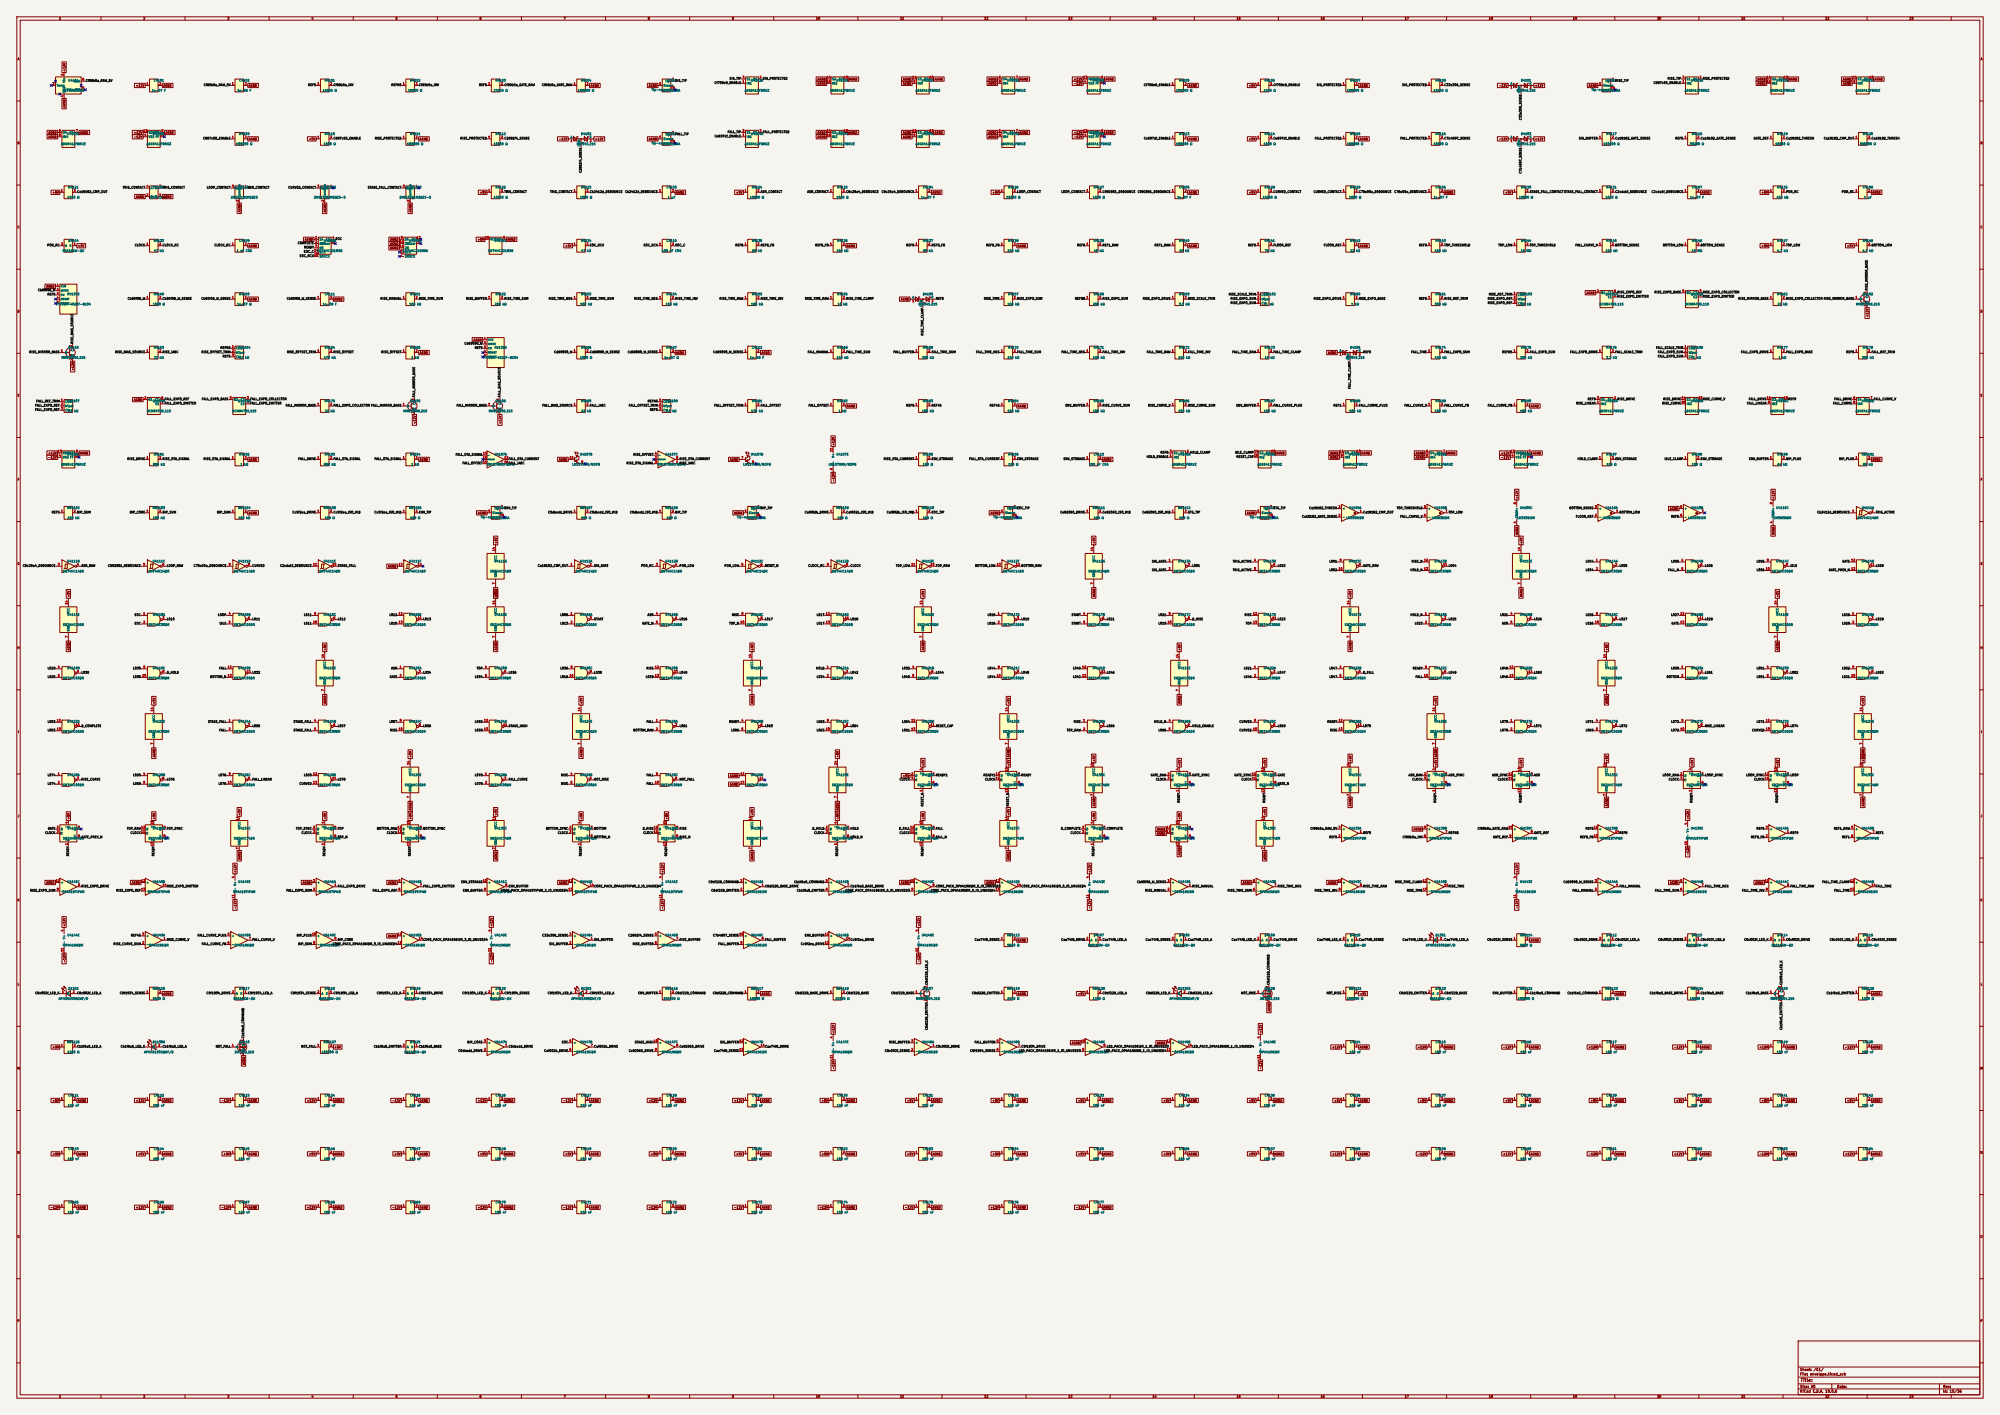
[picture p58: page 15]

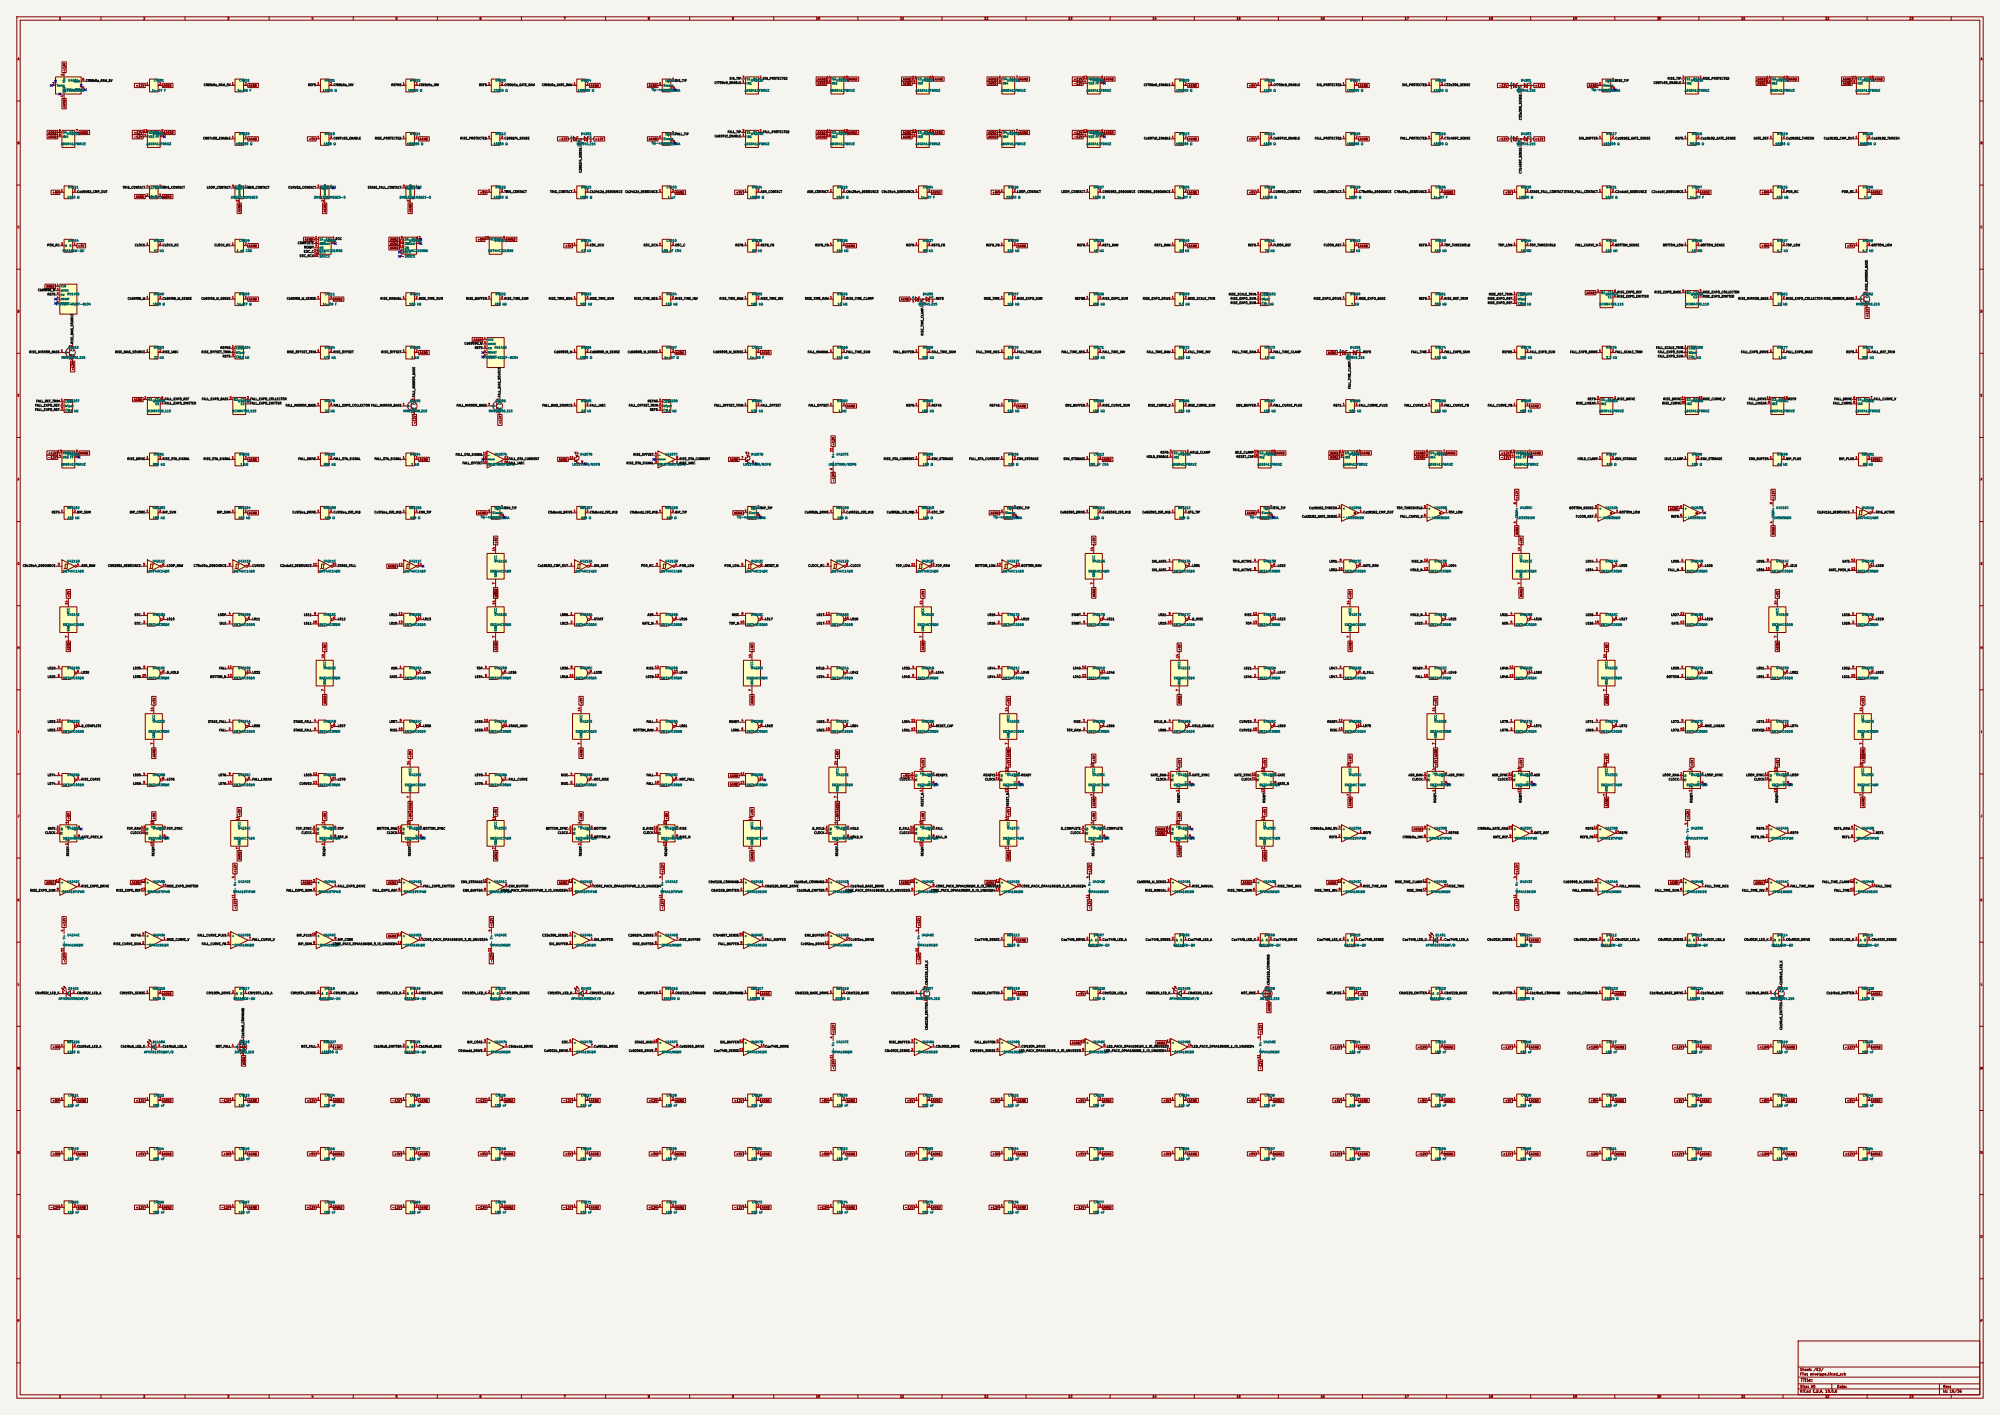
[picture p59: page 16]

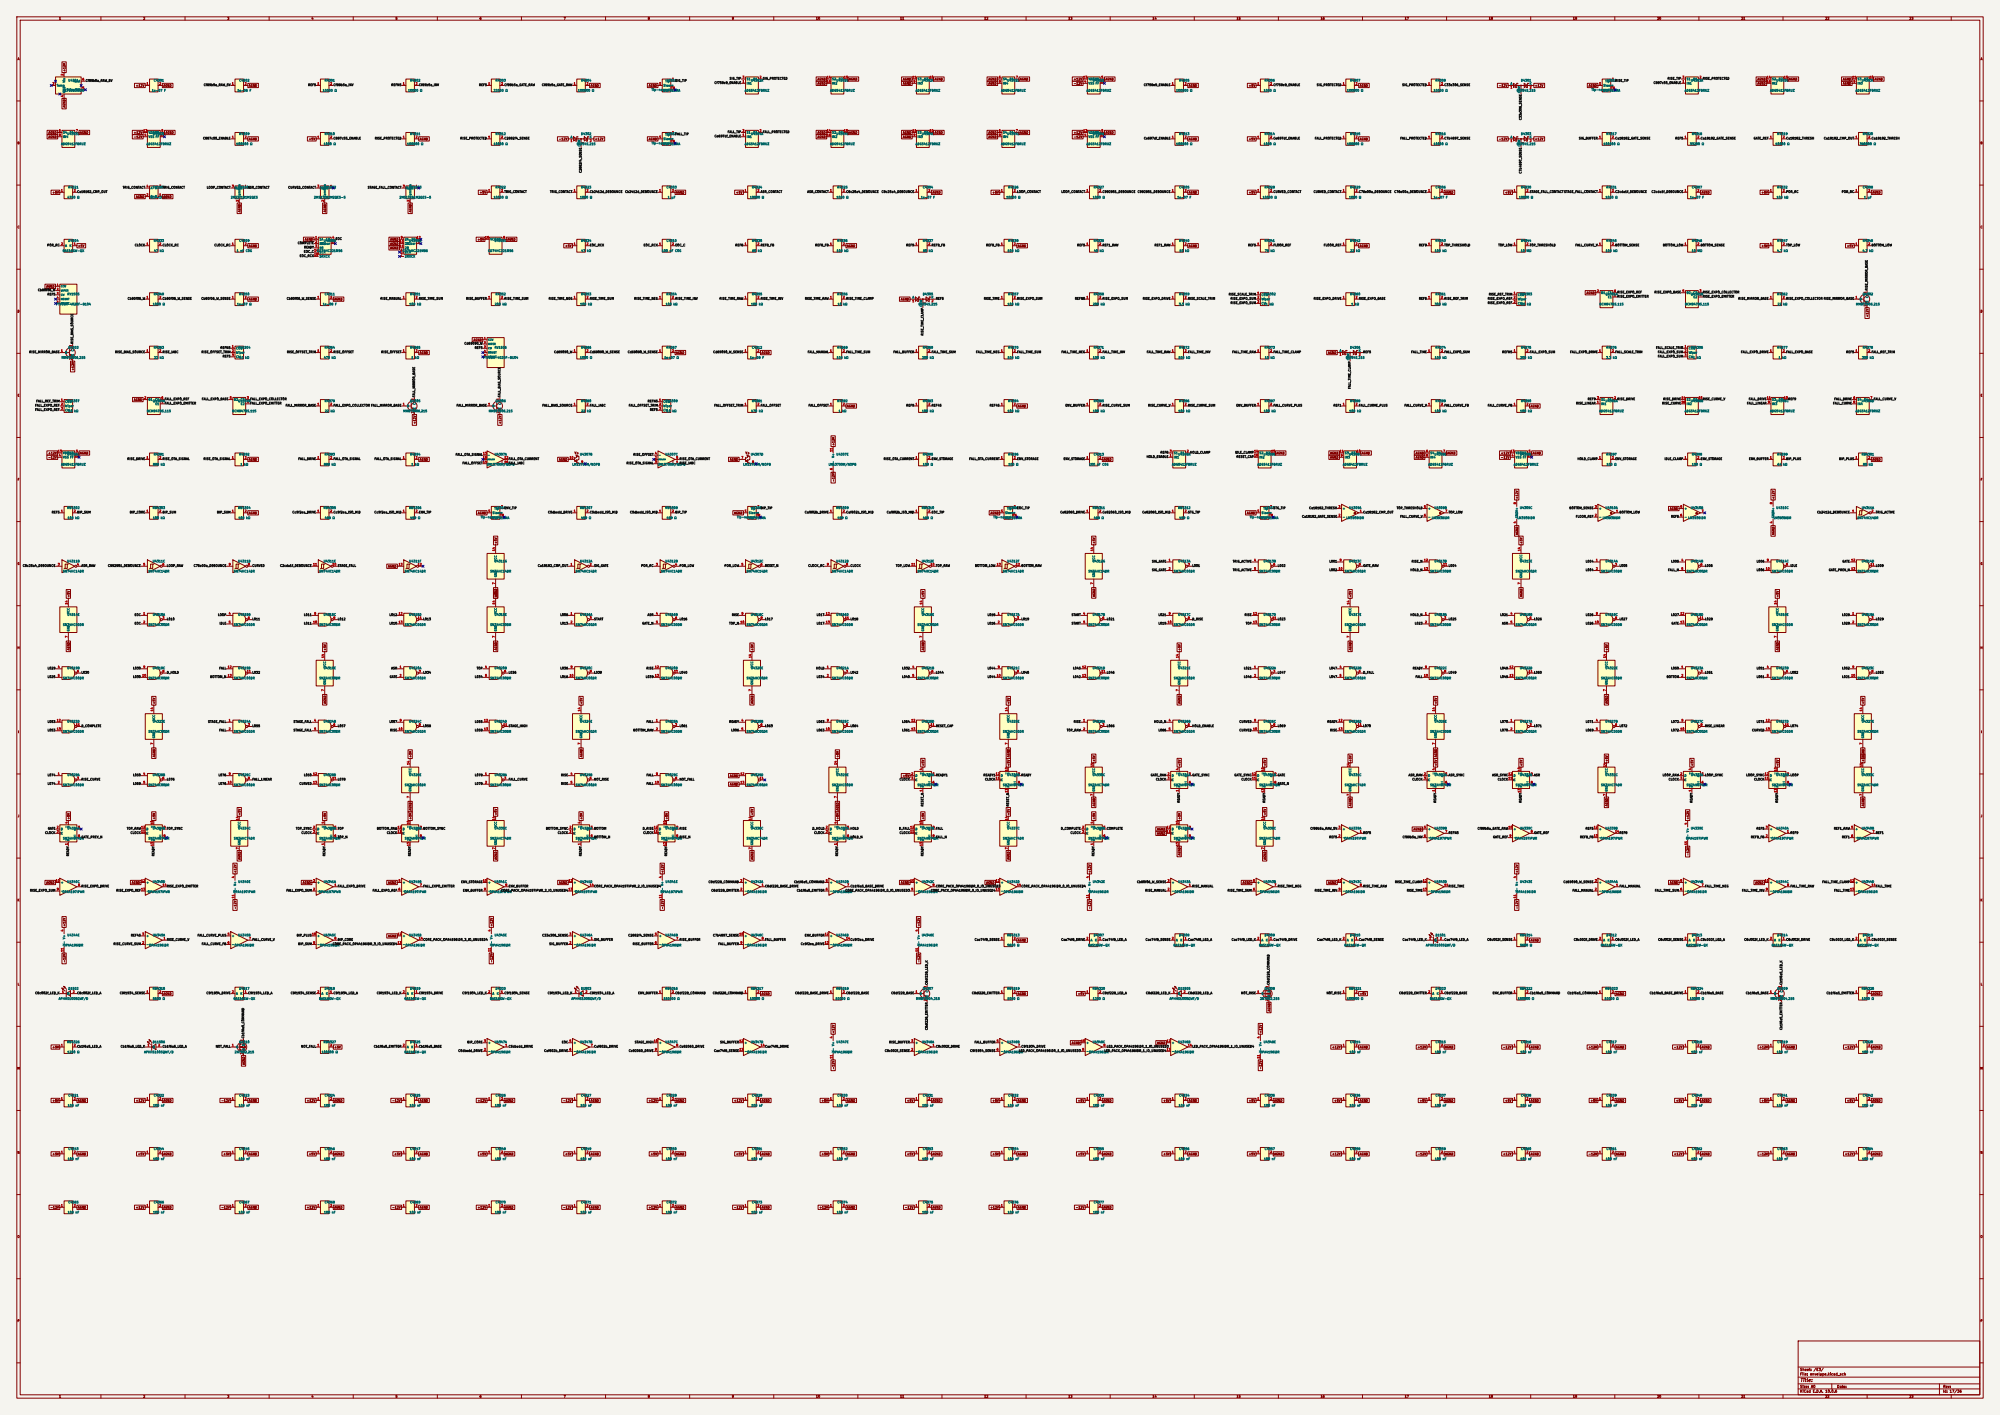
[picture p60: page 17]

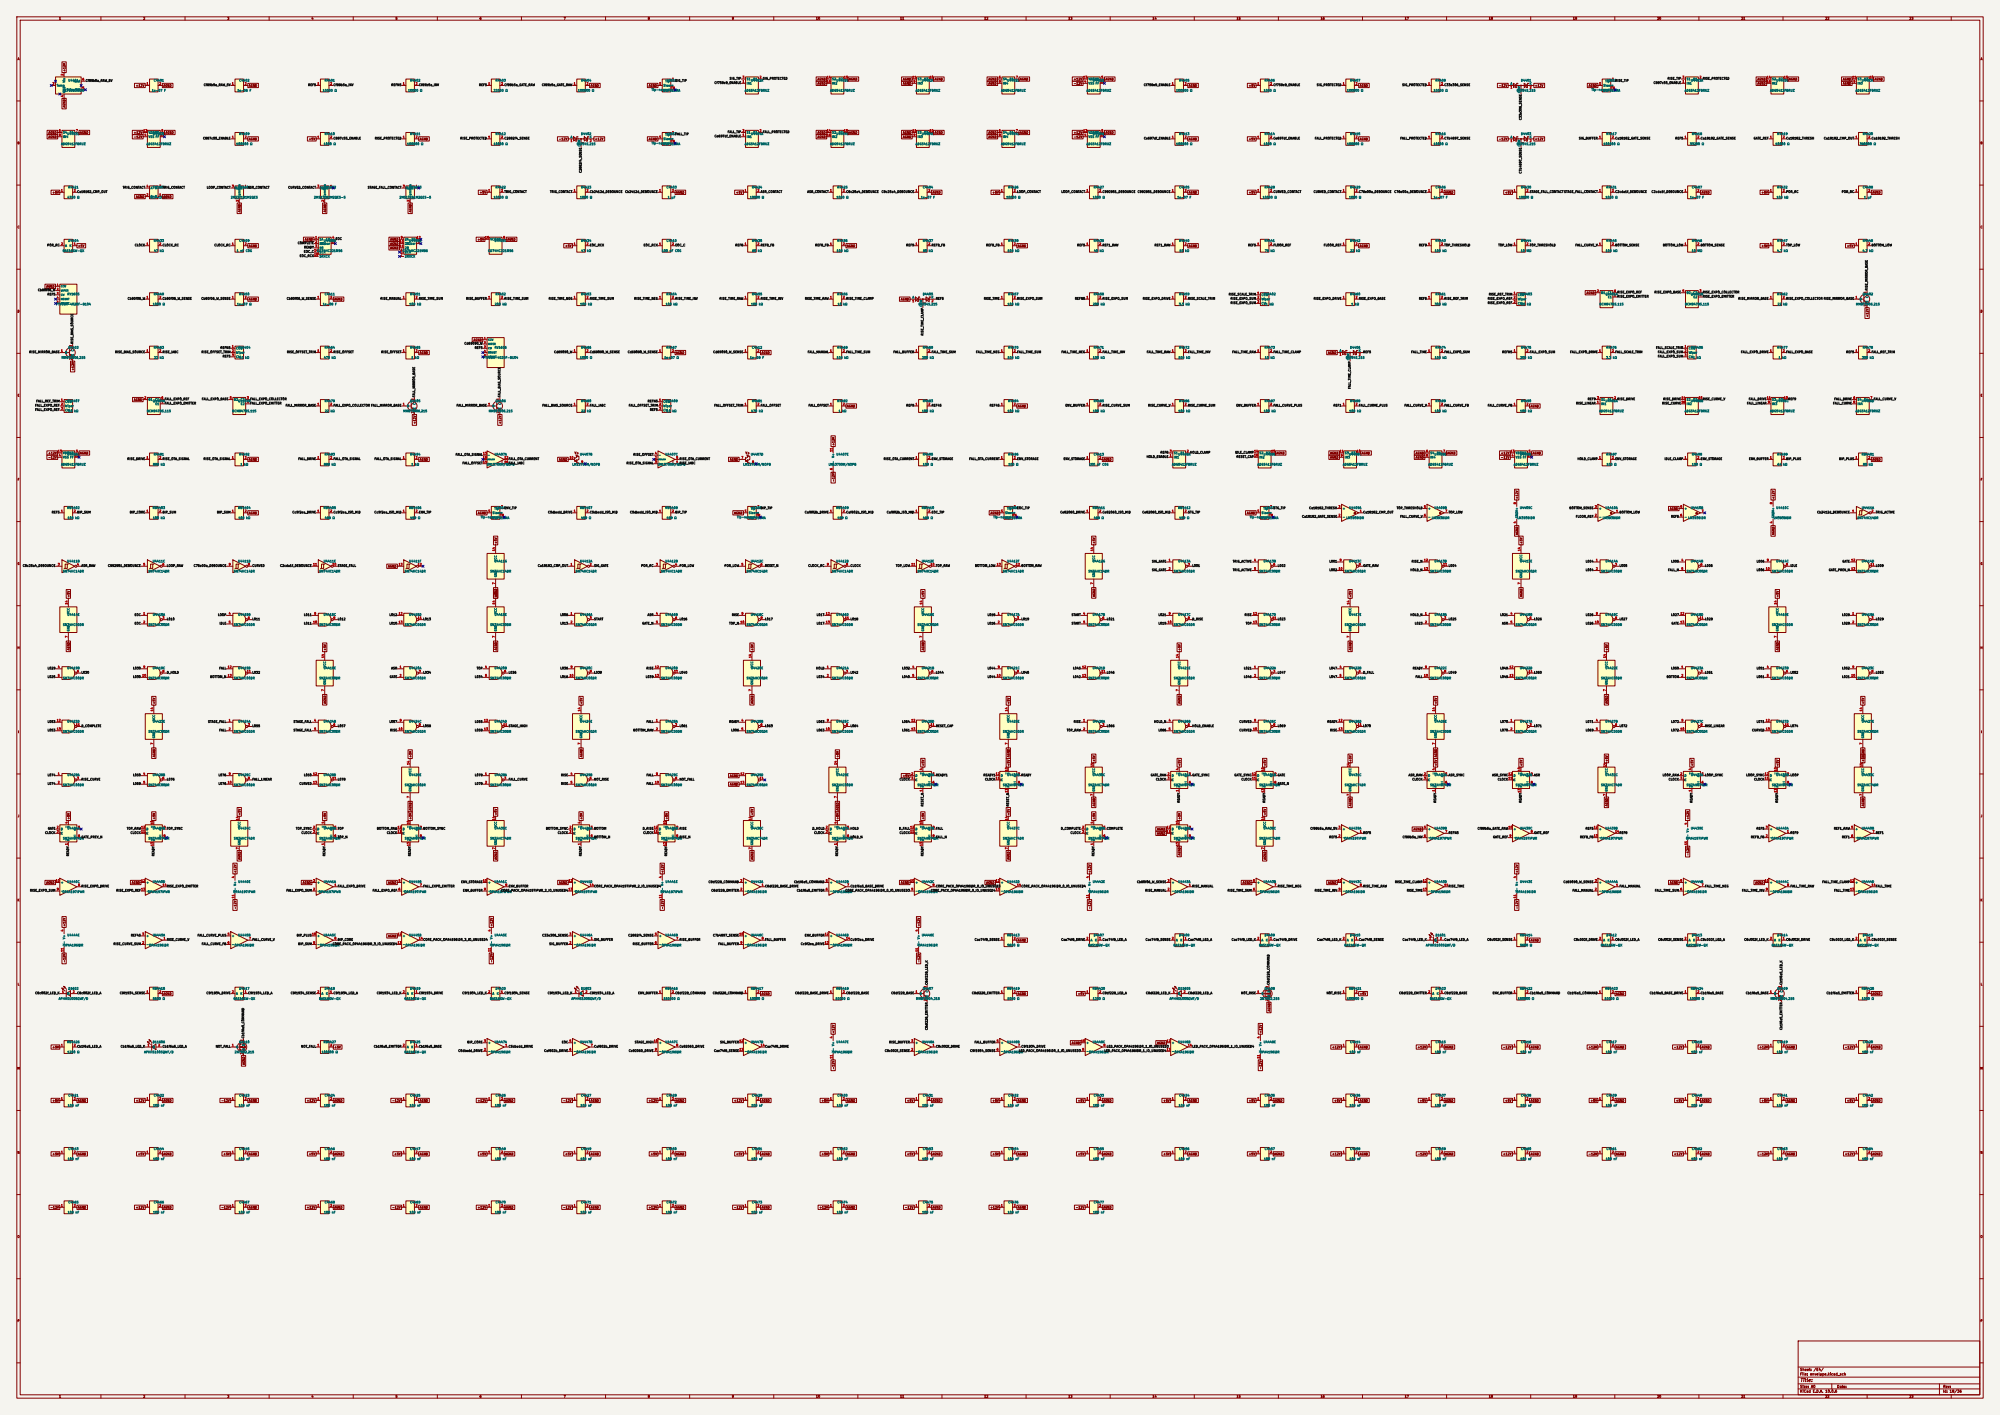
[picture p61: page 18]

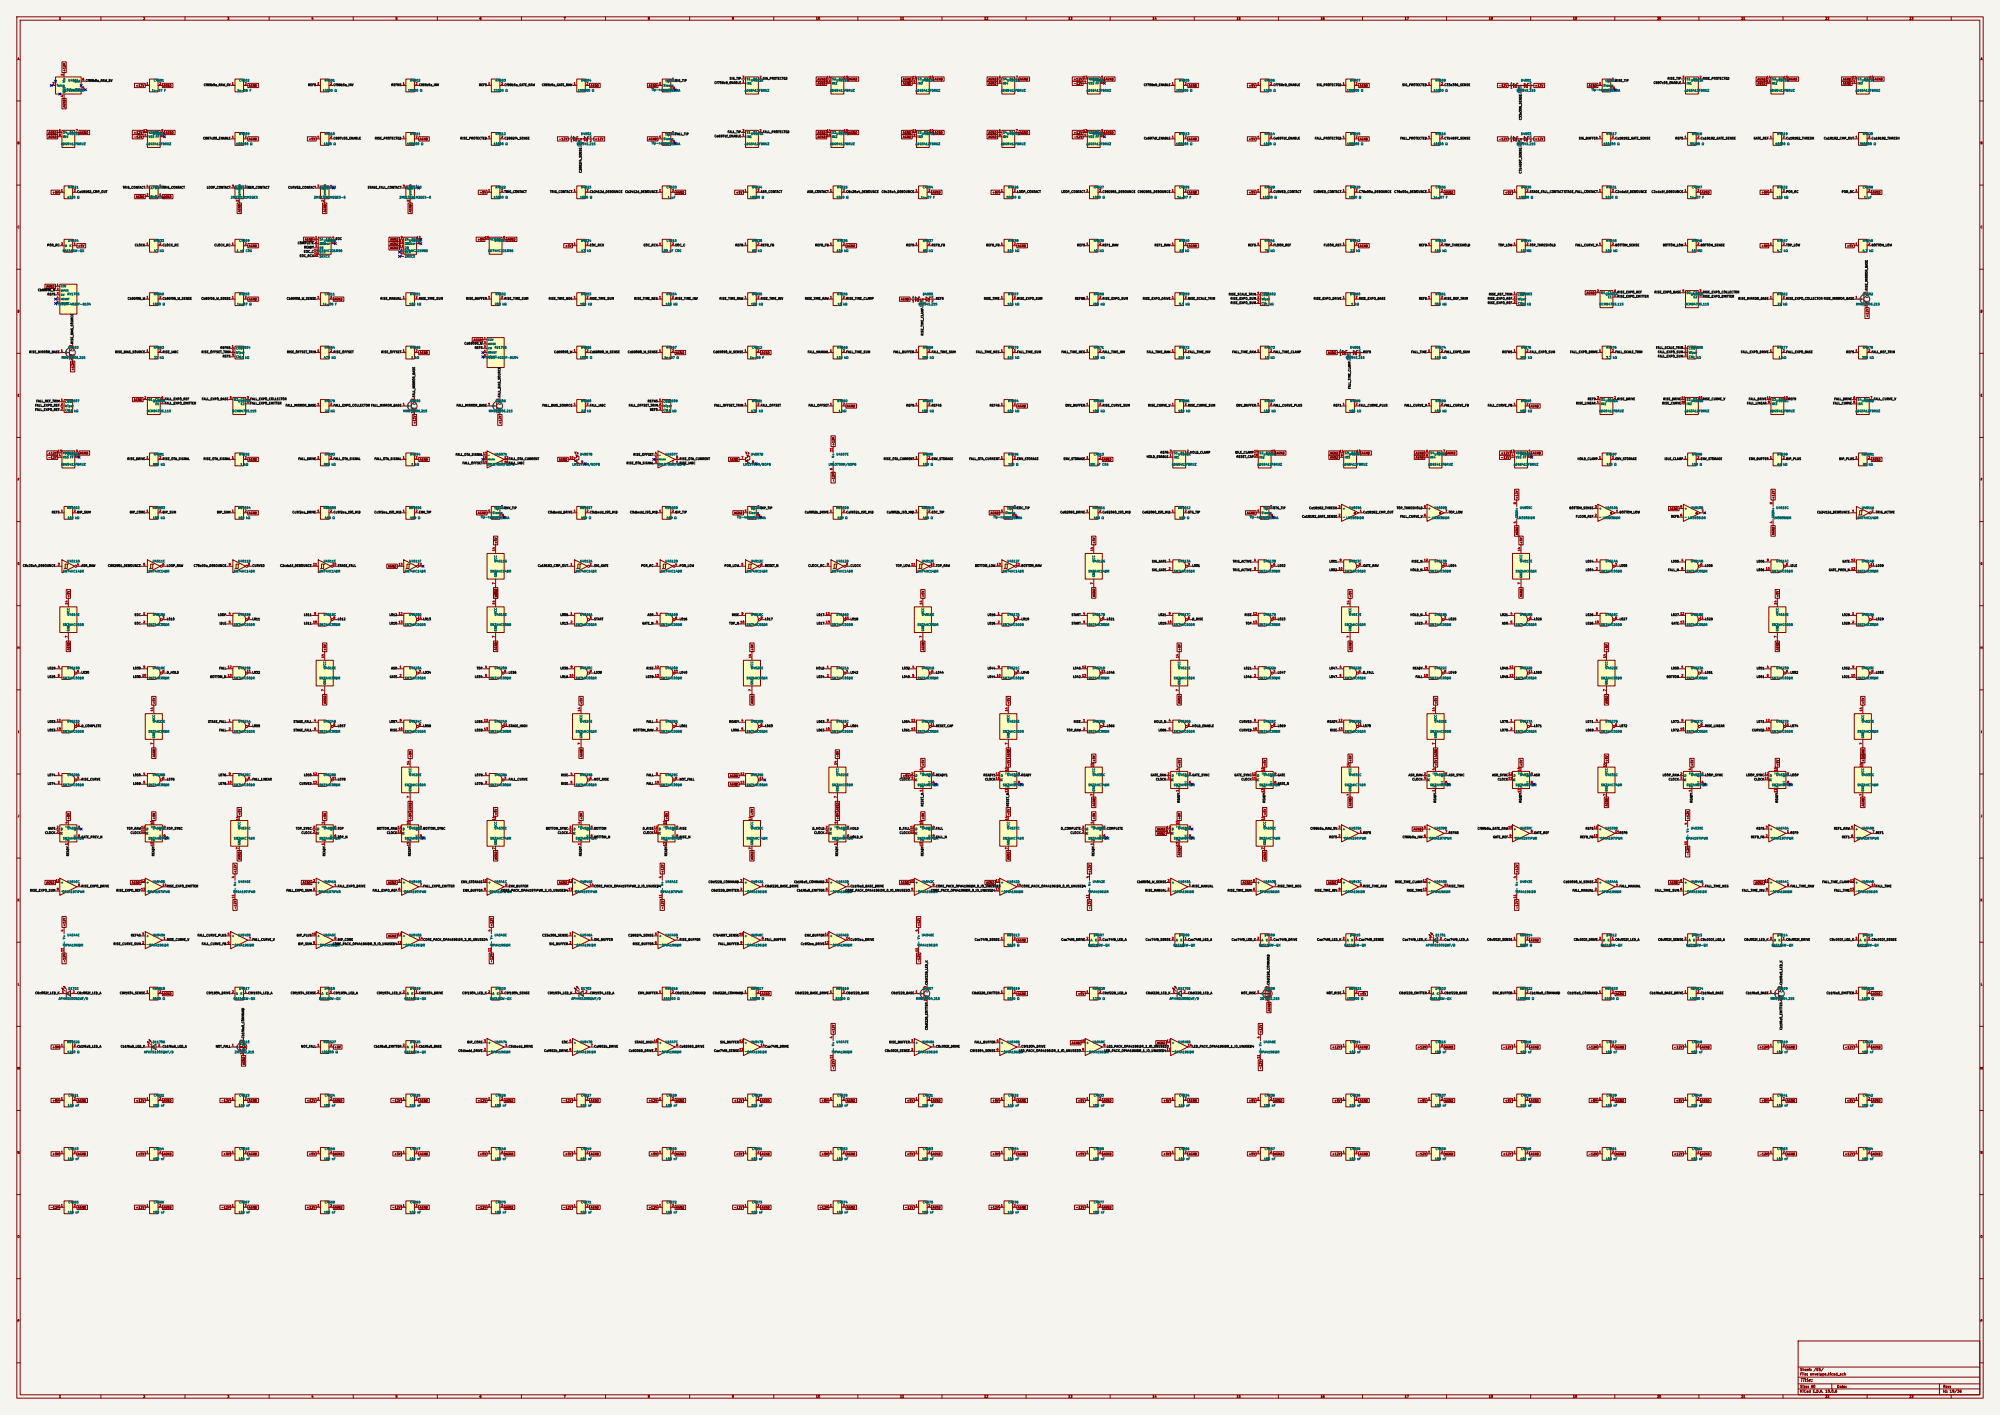
[picture p62: page 19]

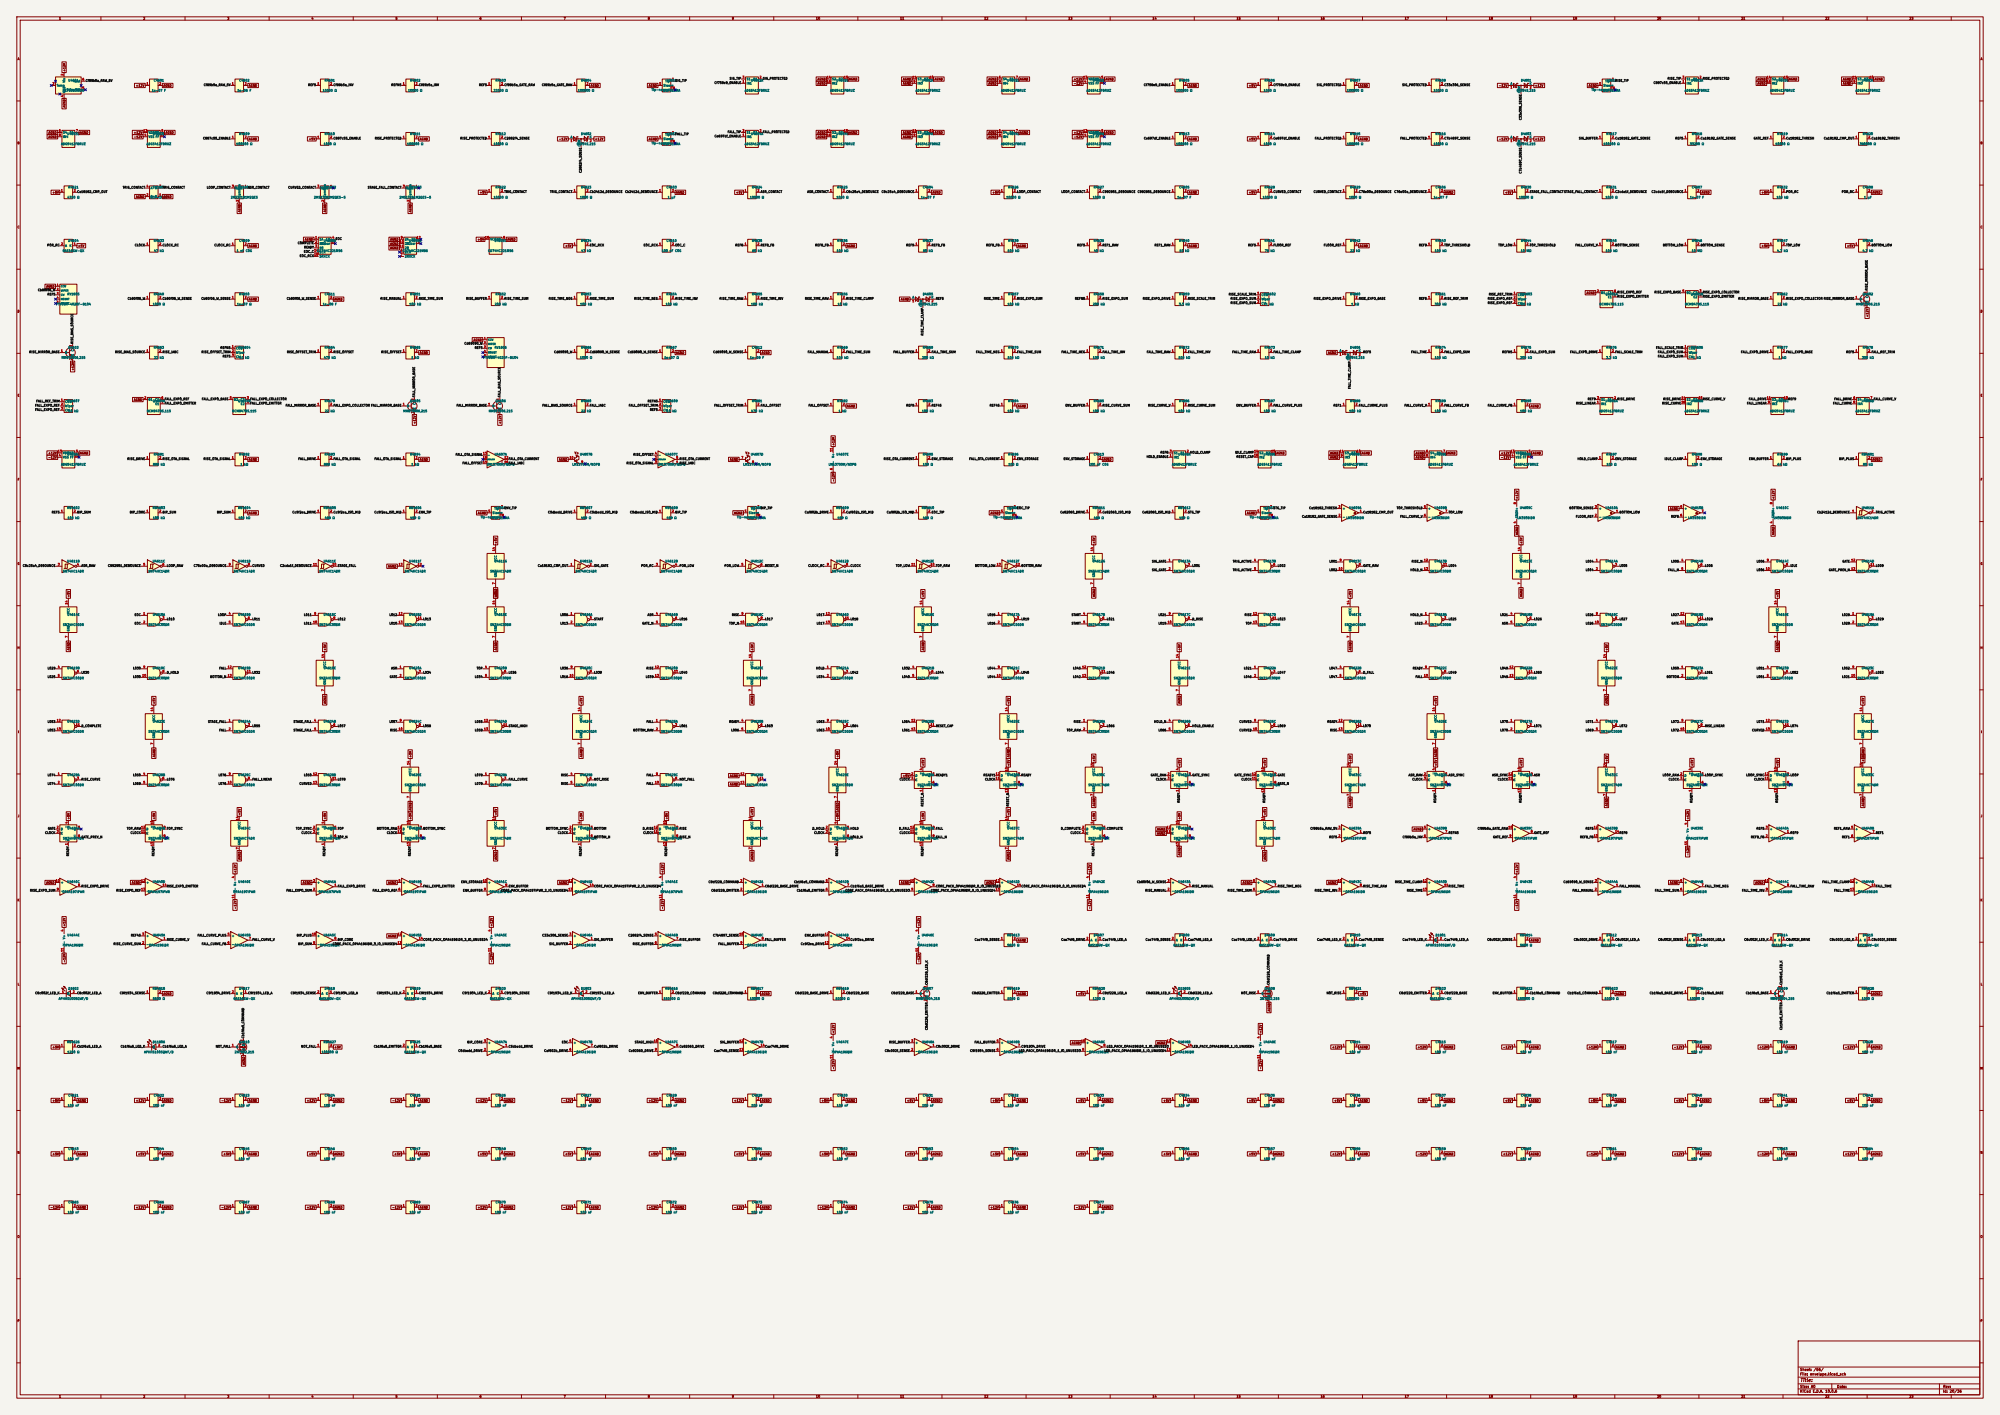
[picture p63: page 20]

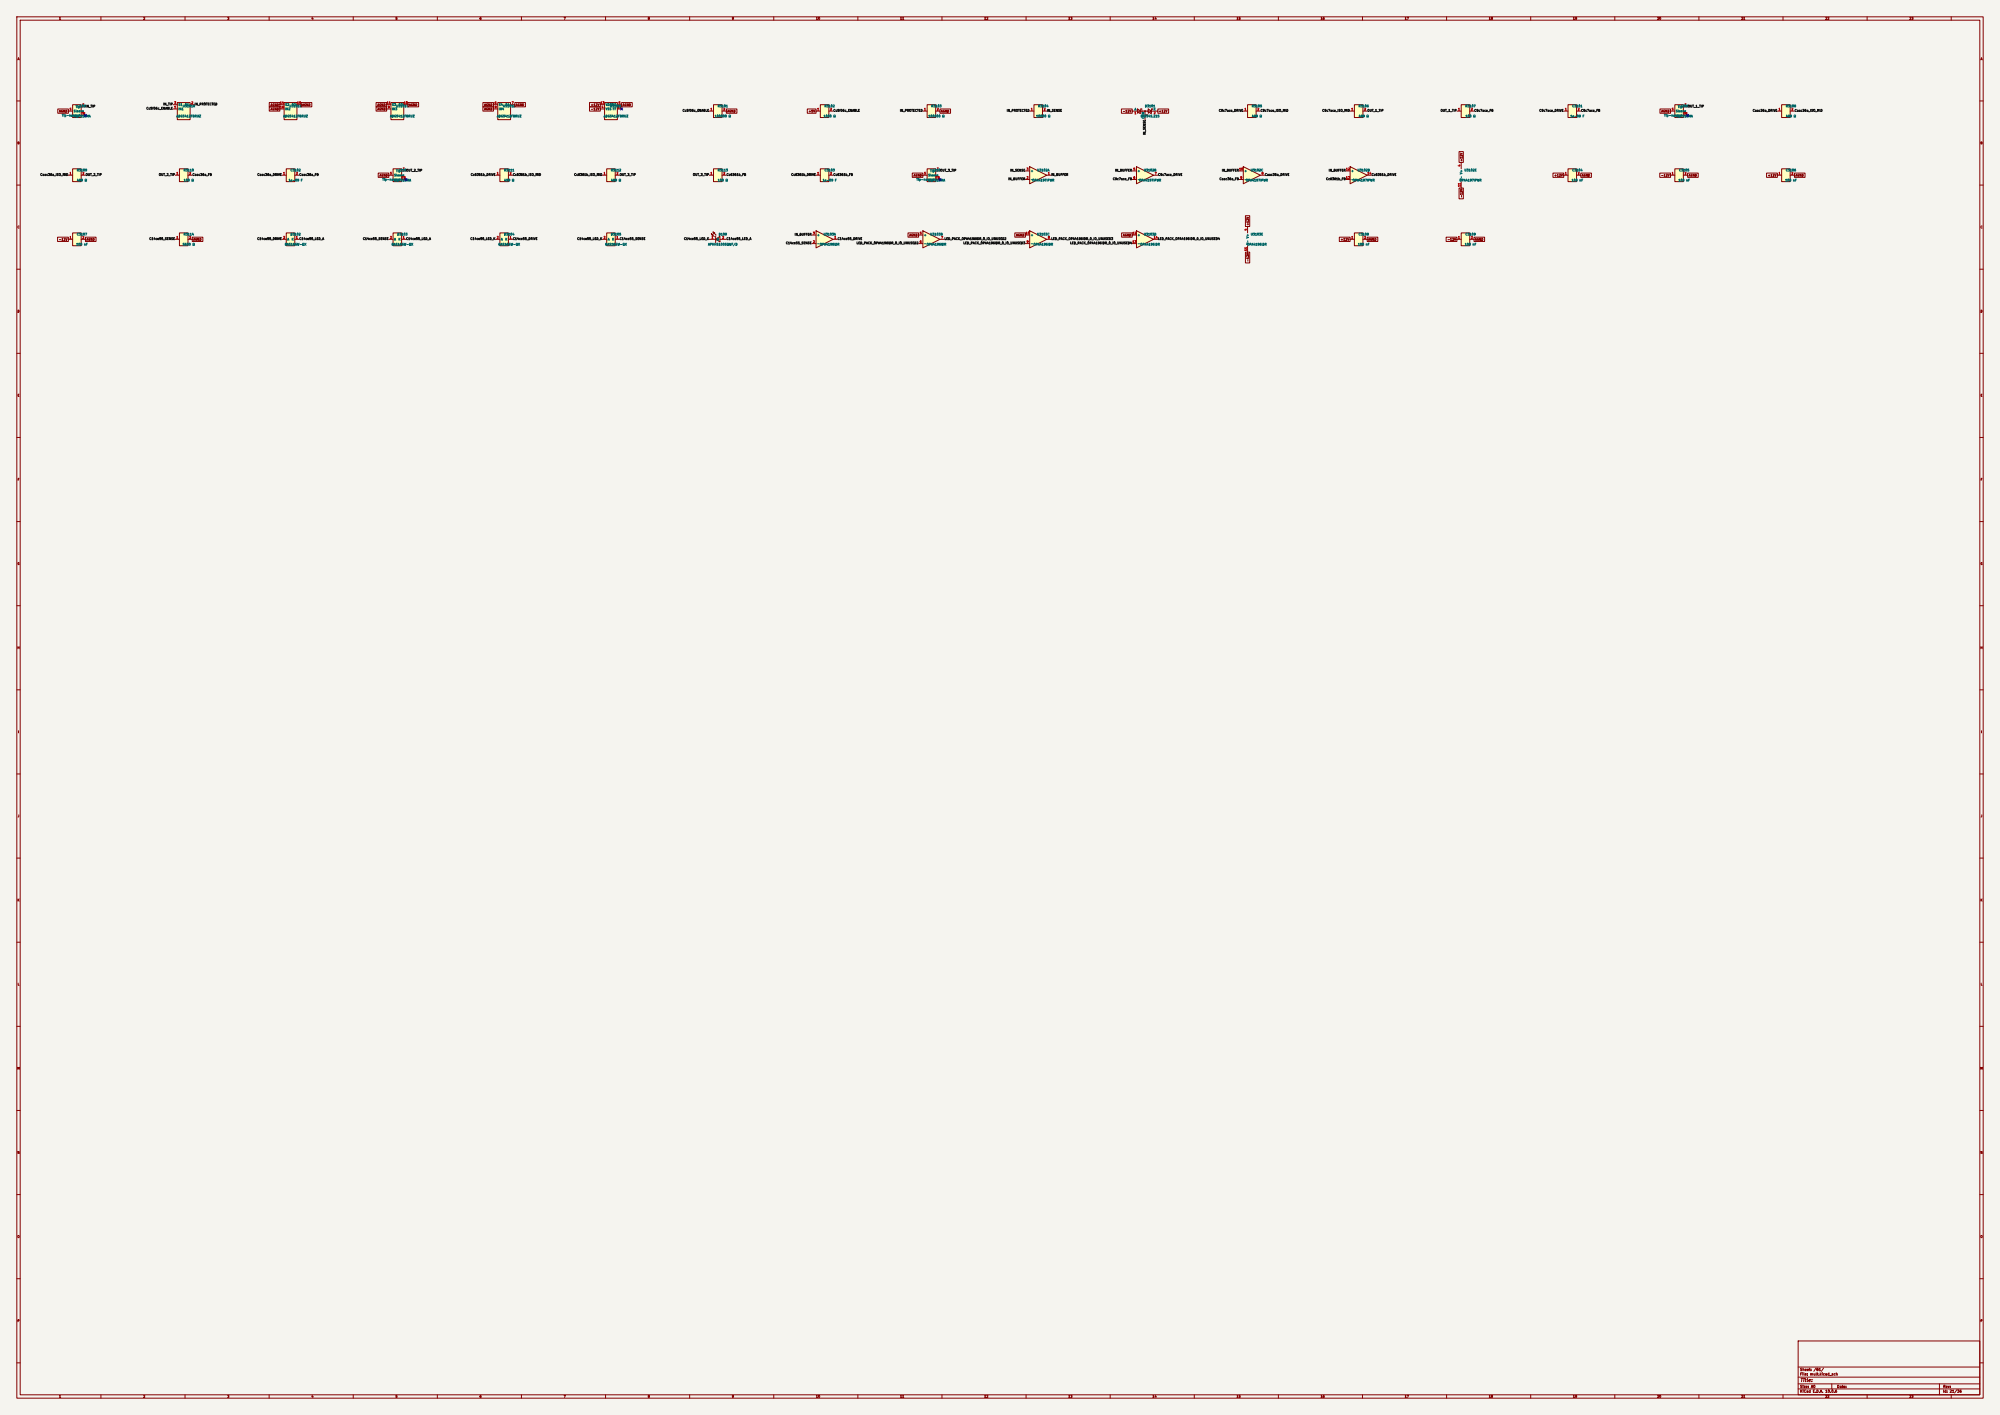
[picture p64: page 21]

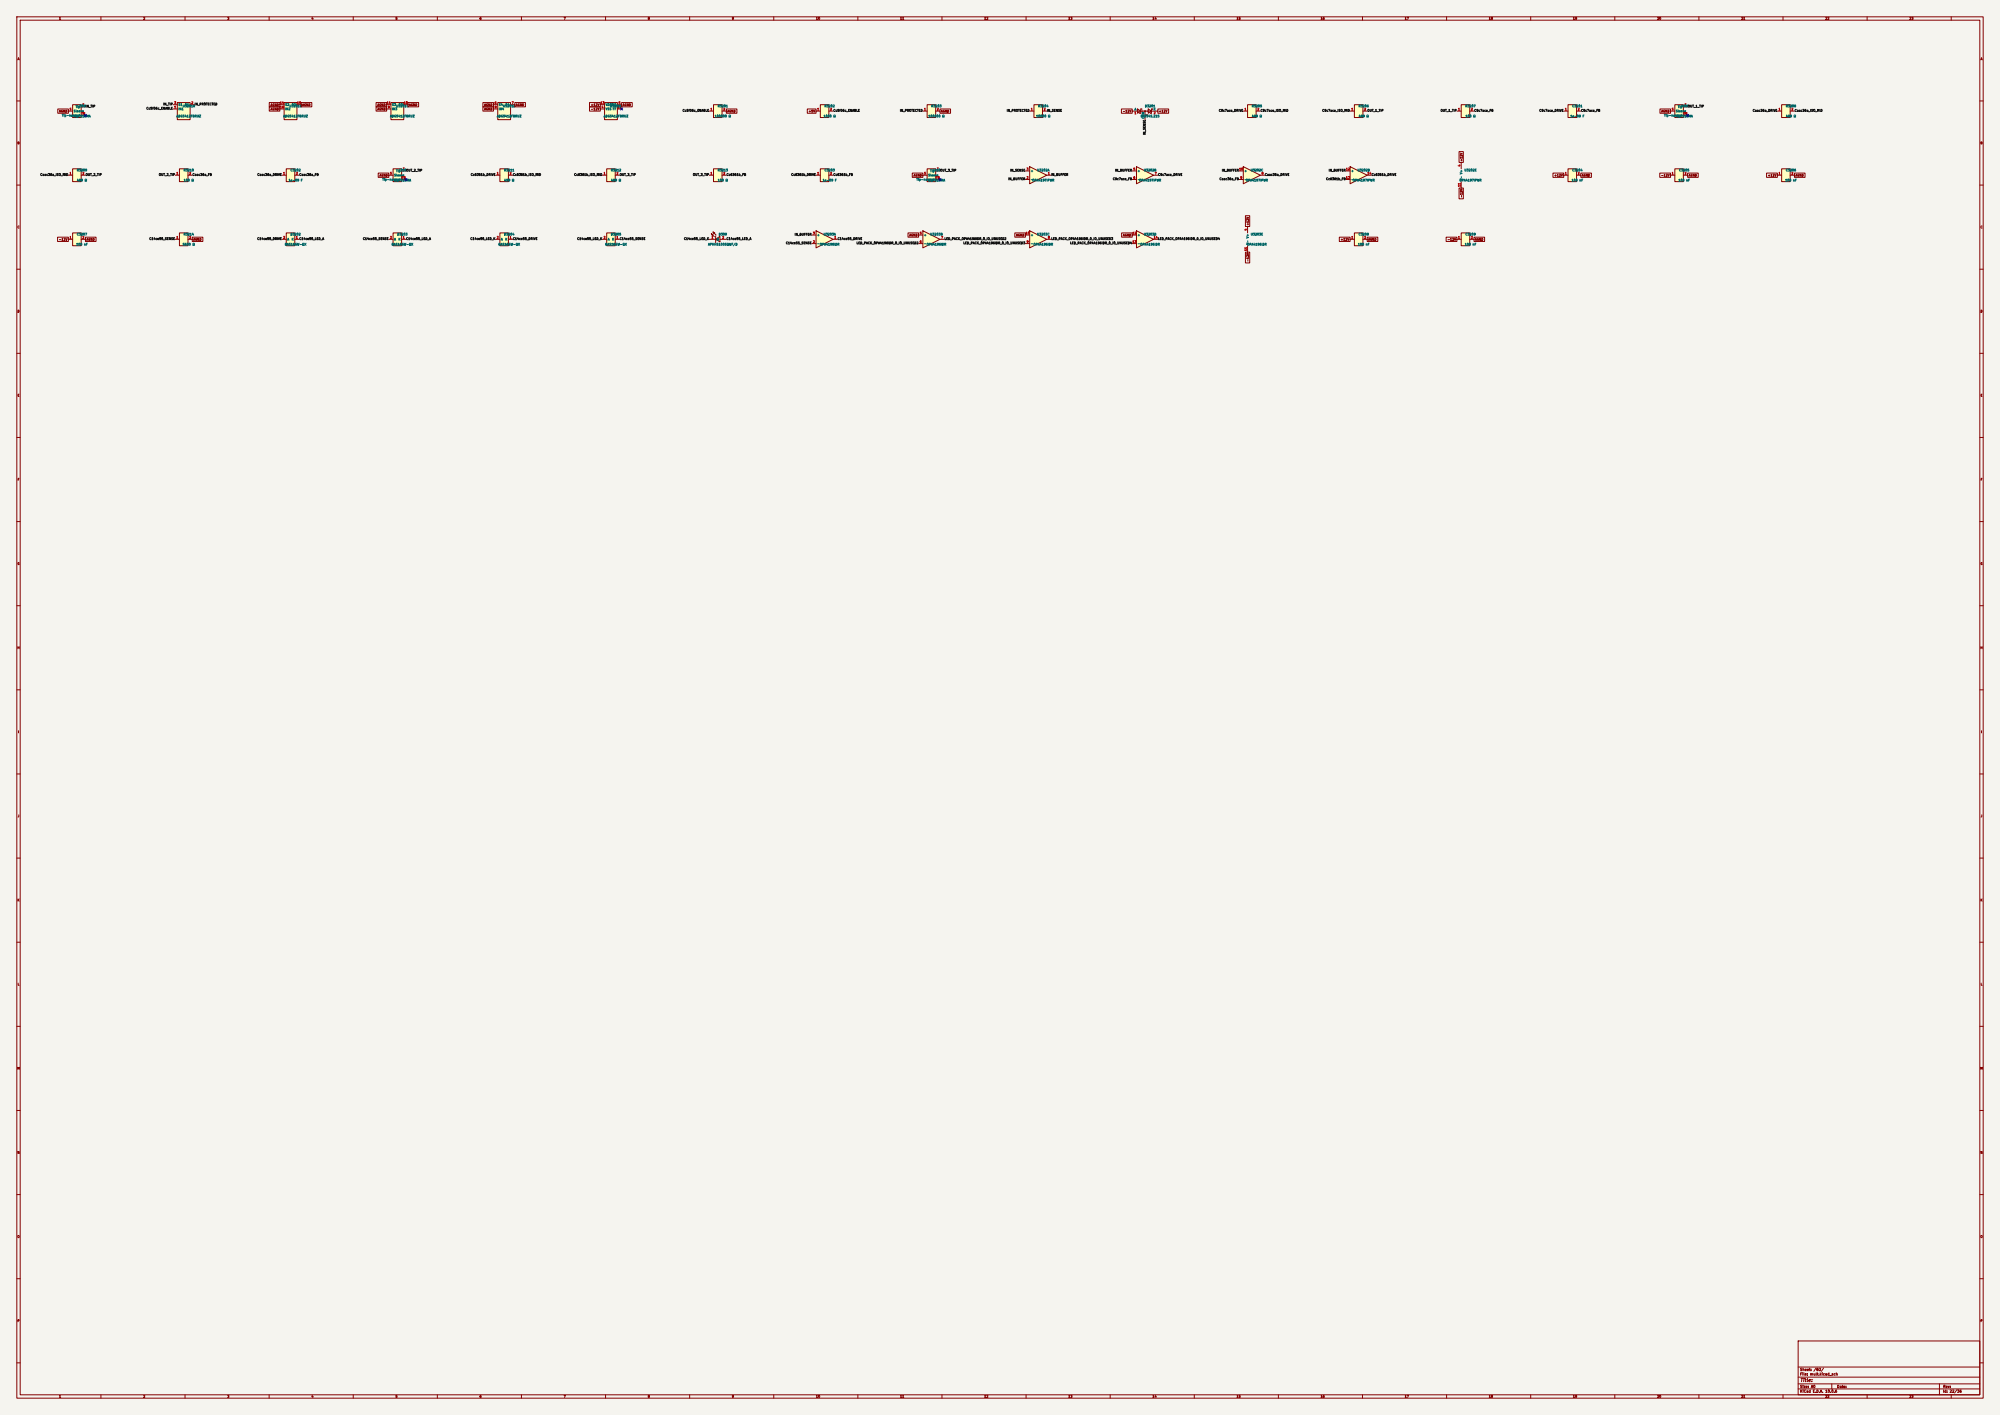
[picture p65: page 22]

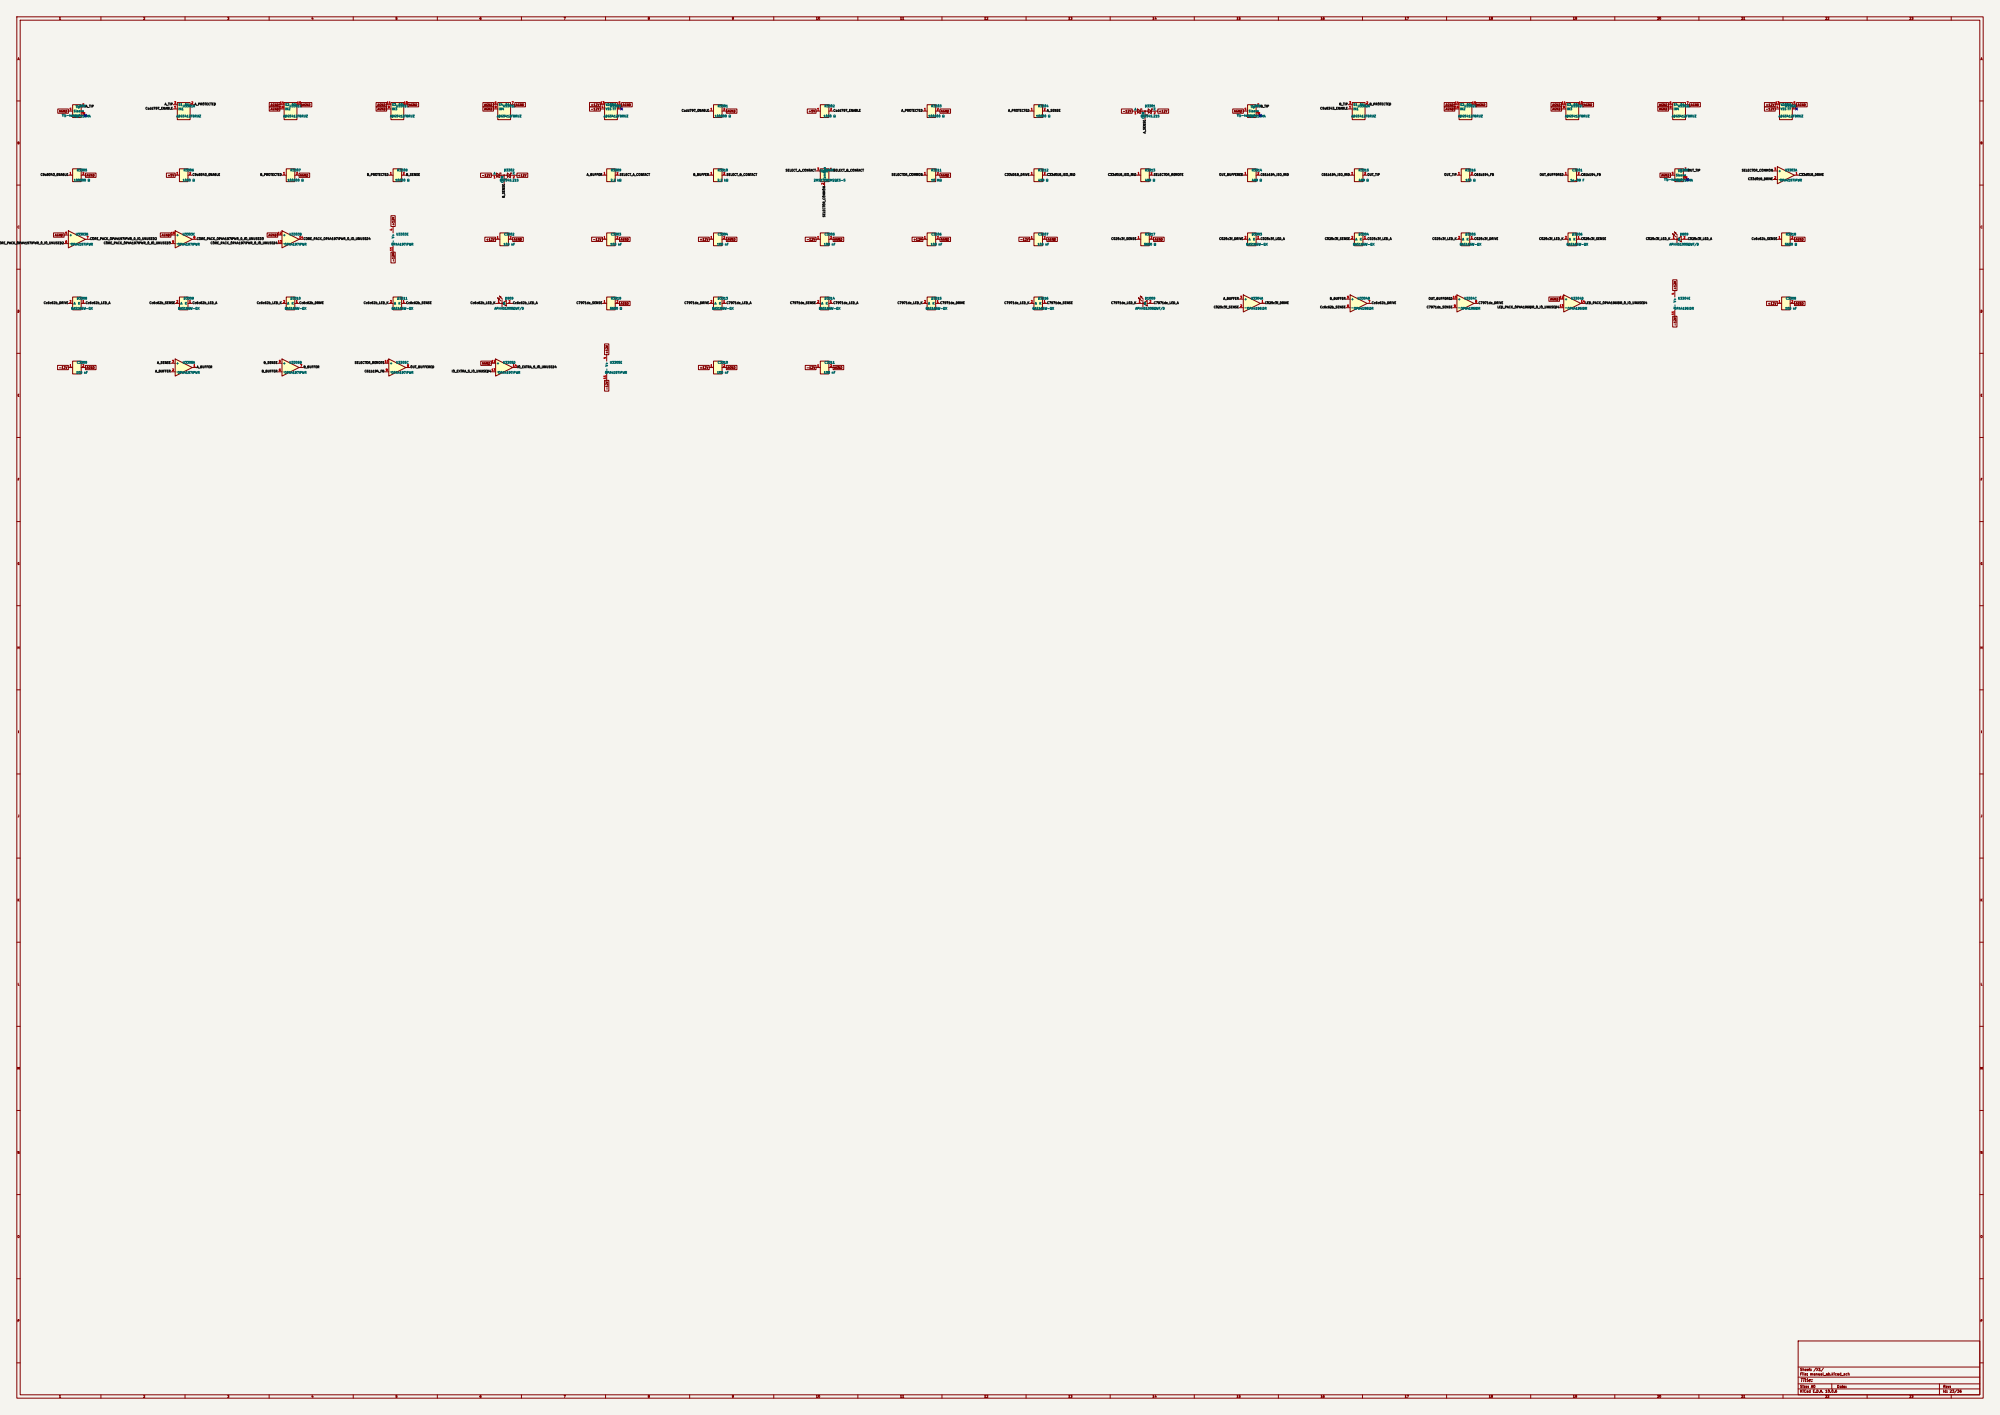
[picture p66: page 23]

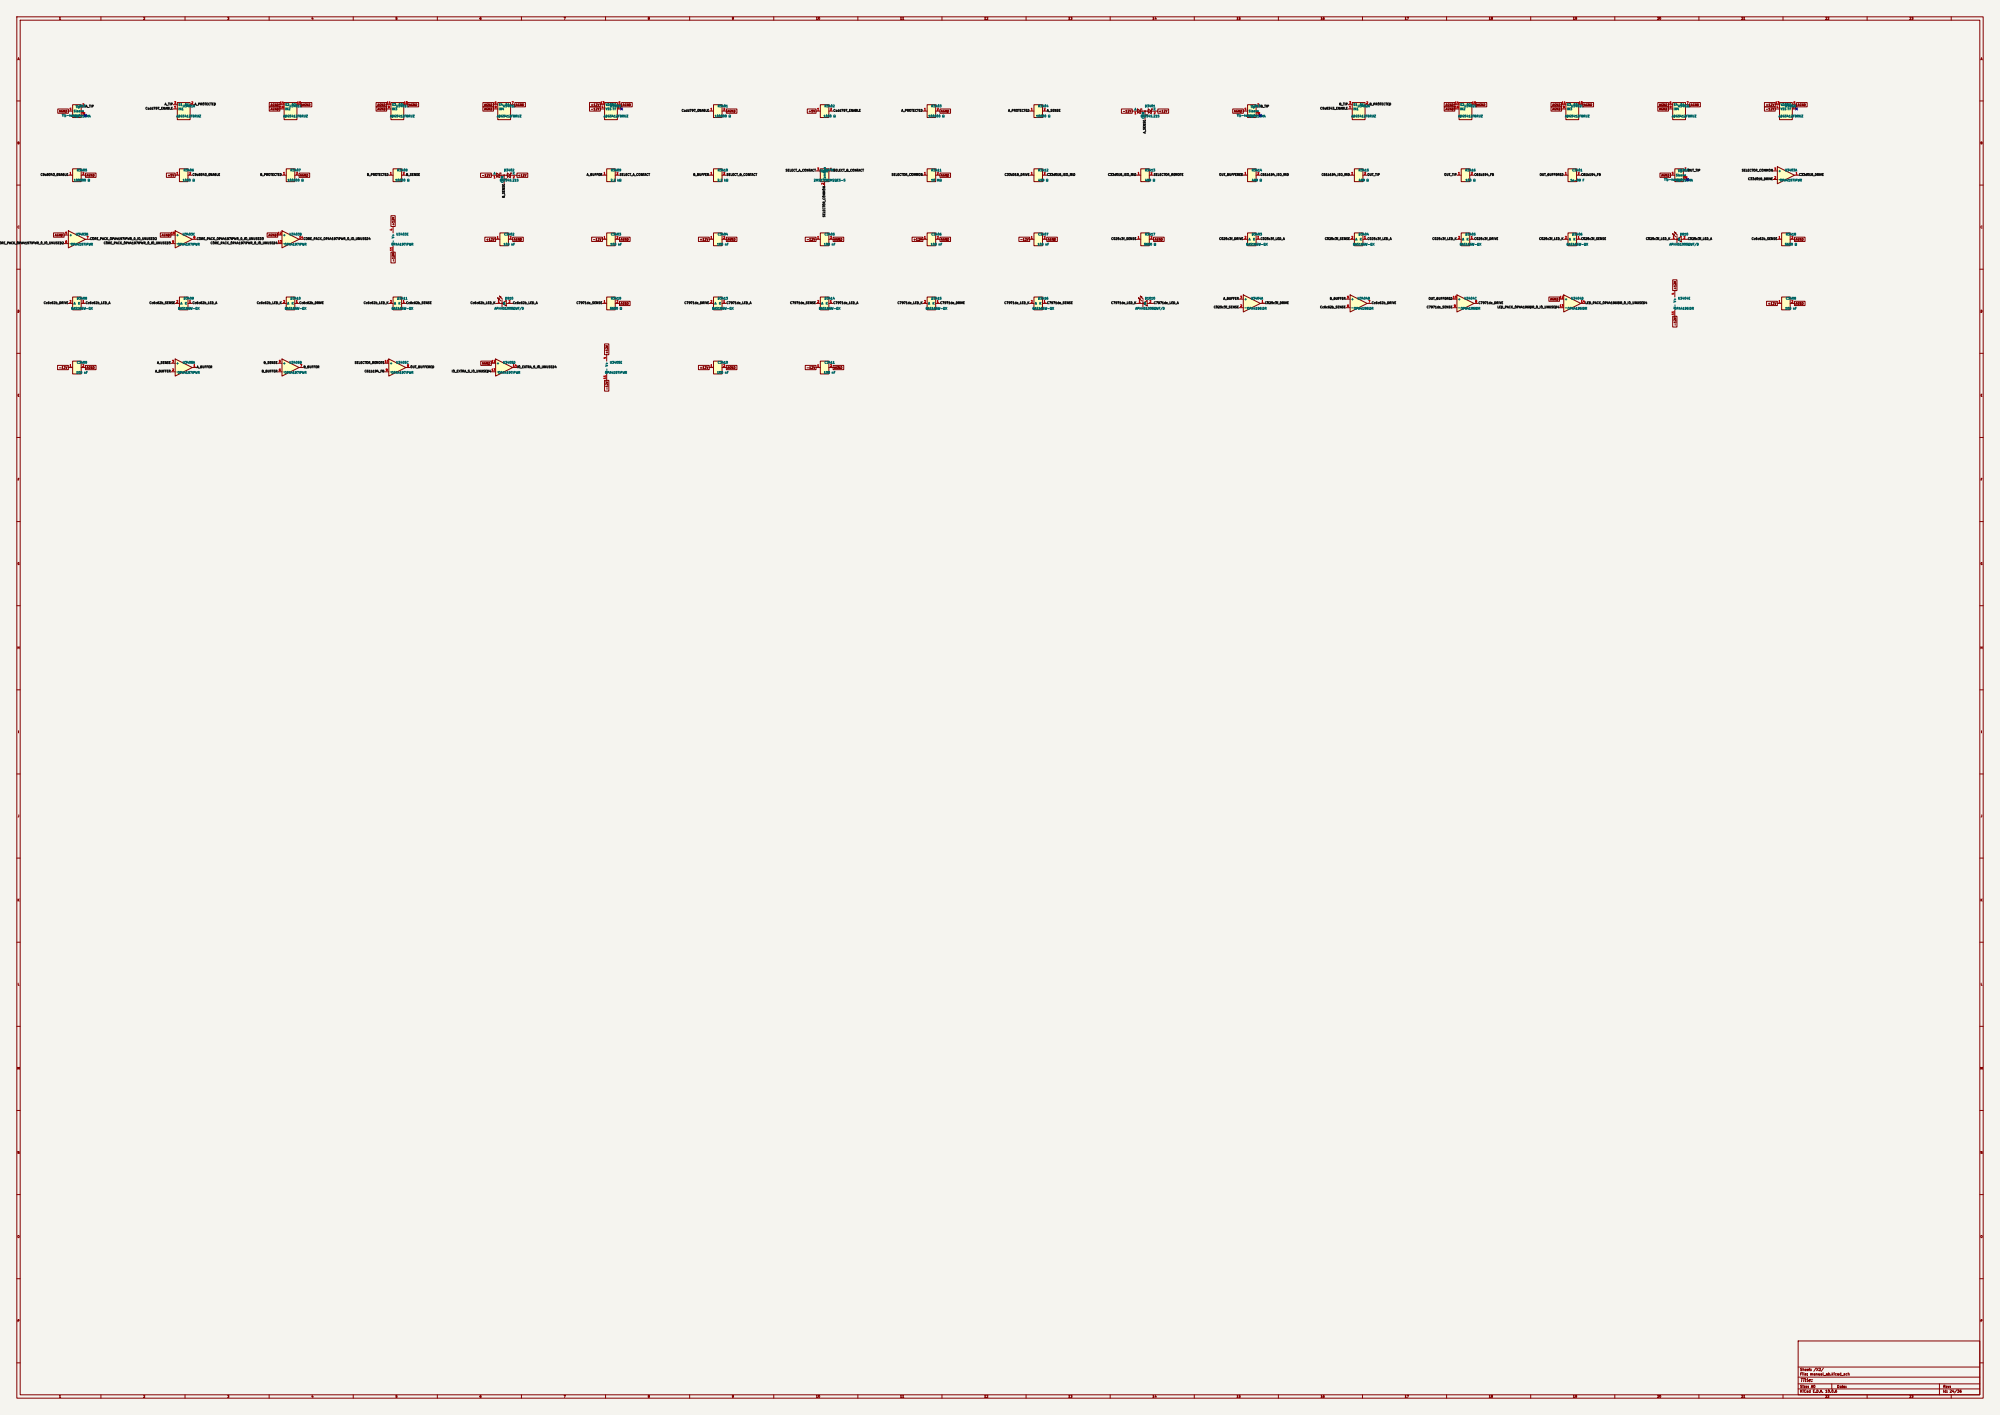
[picture p67: page 24]

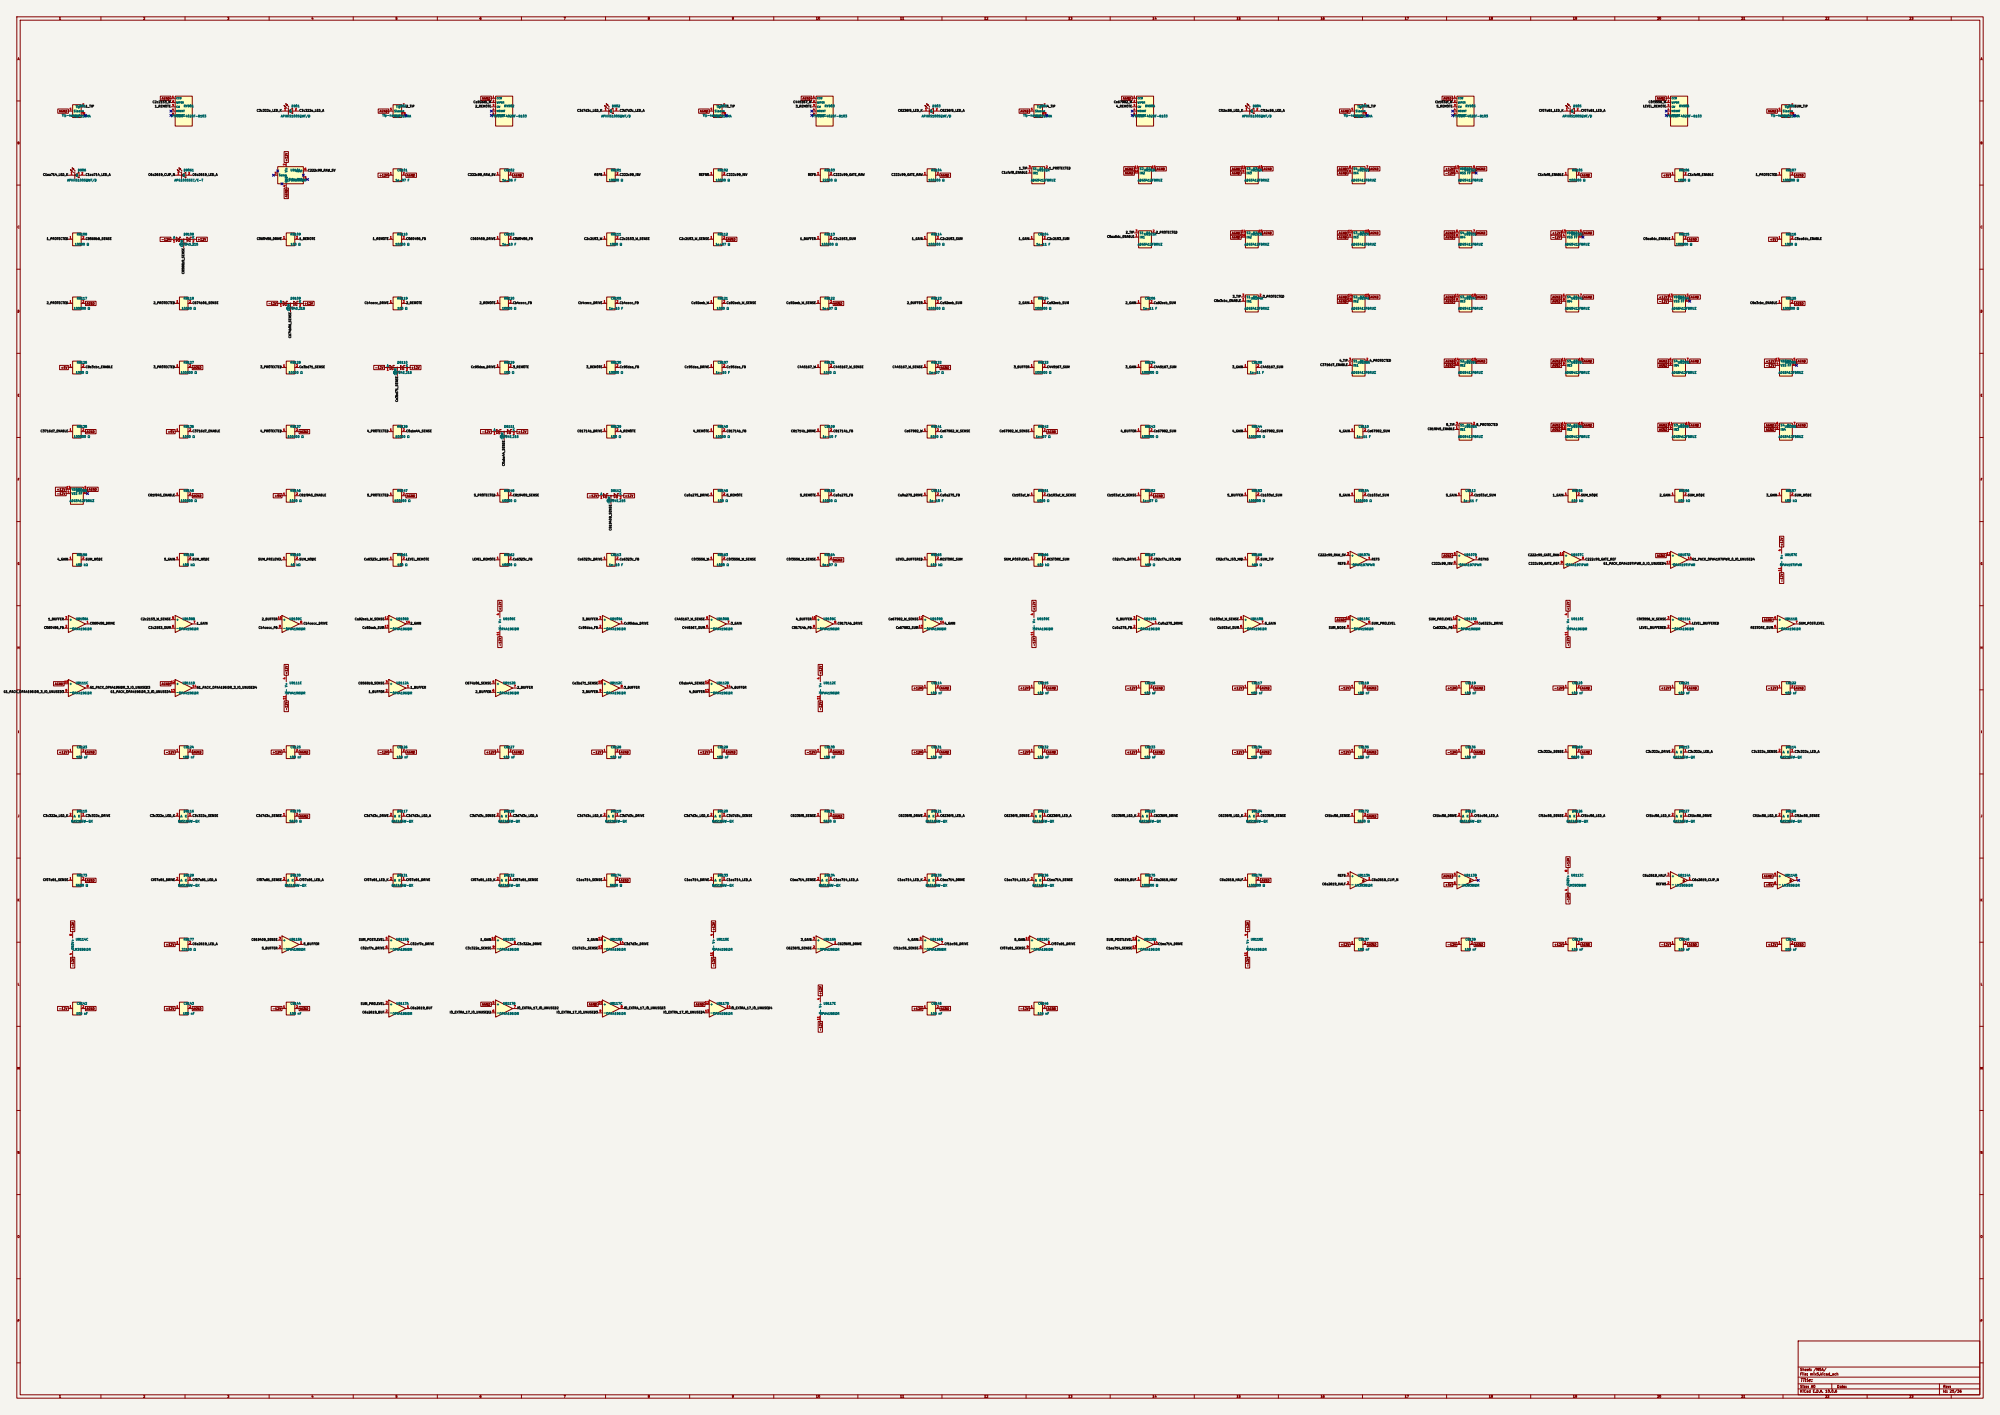
[picture p68: page 25]

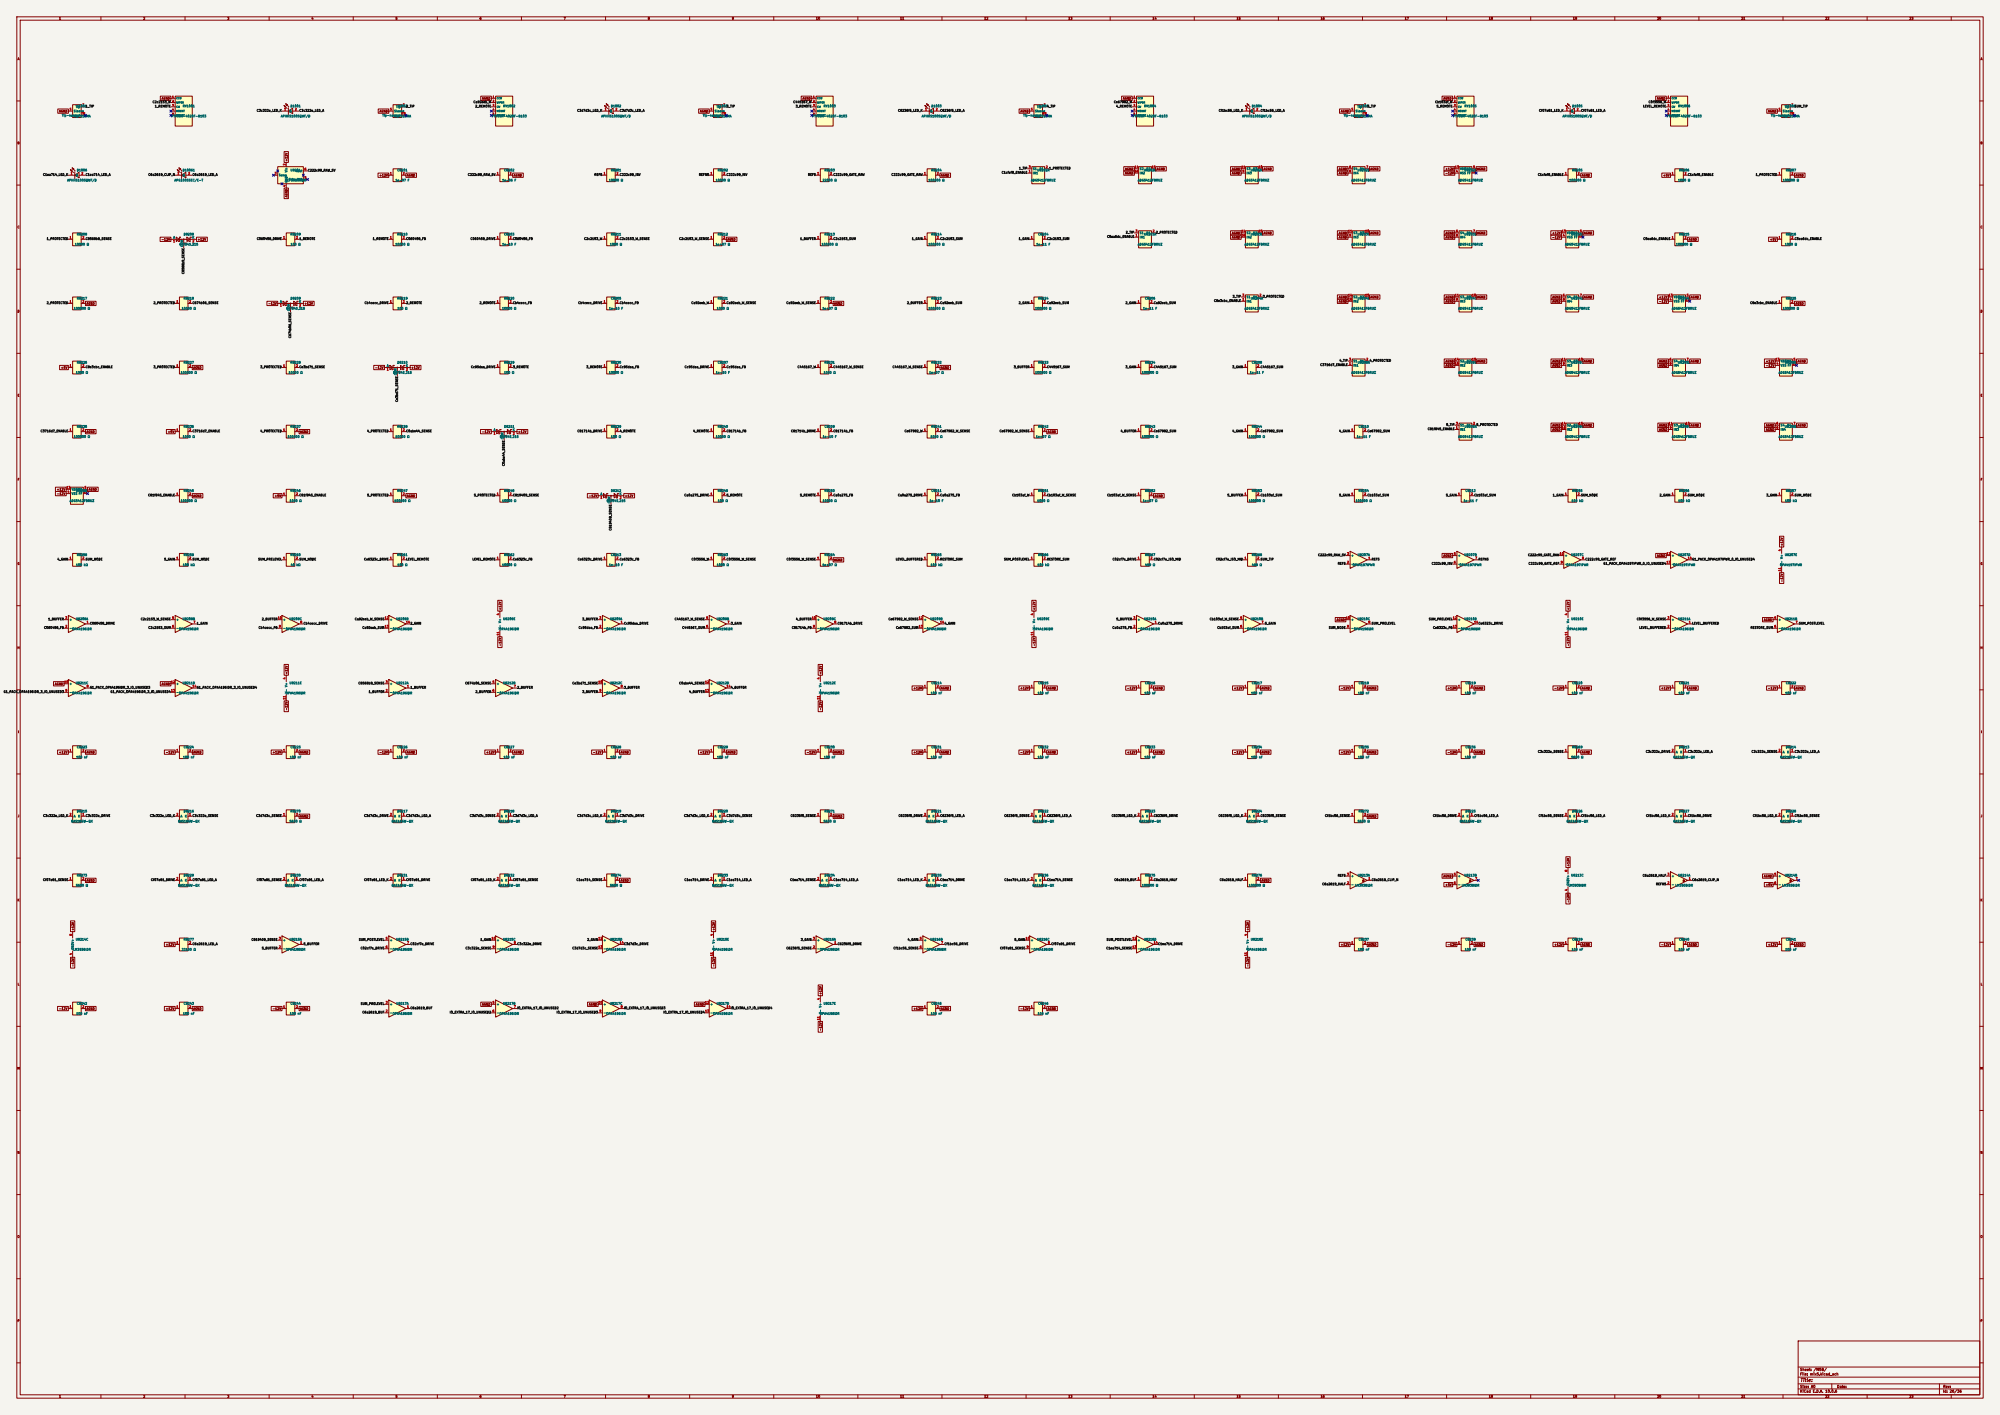
[picture p69: page 26]

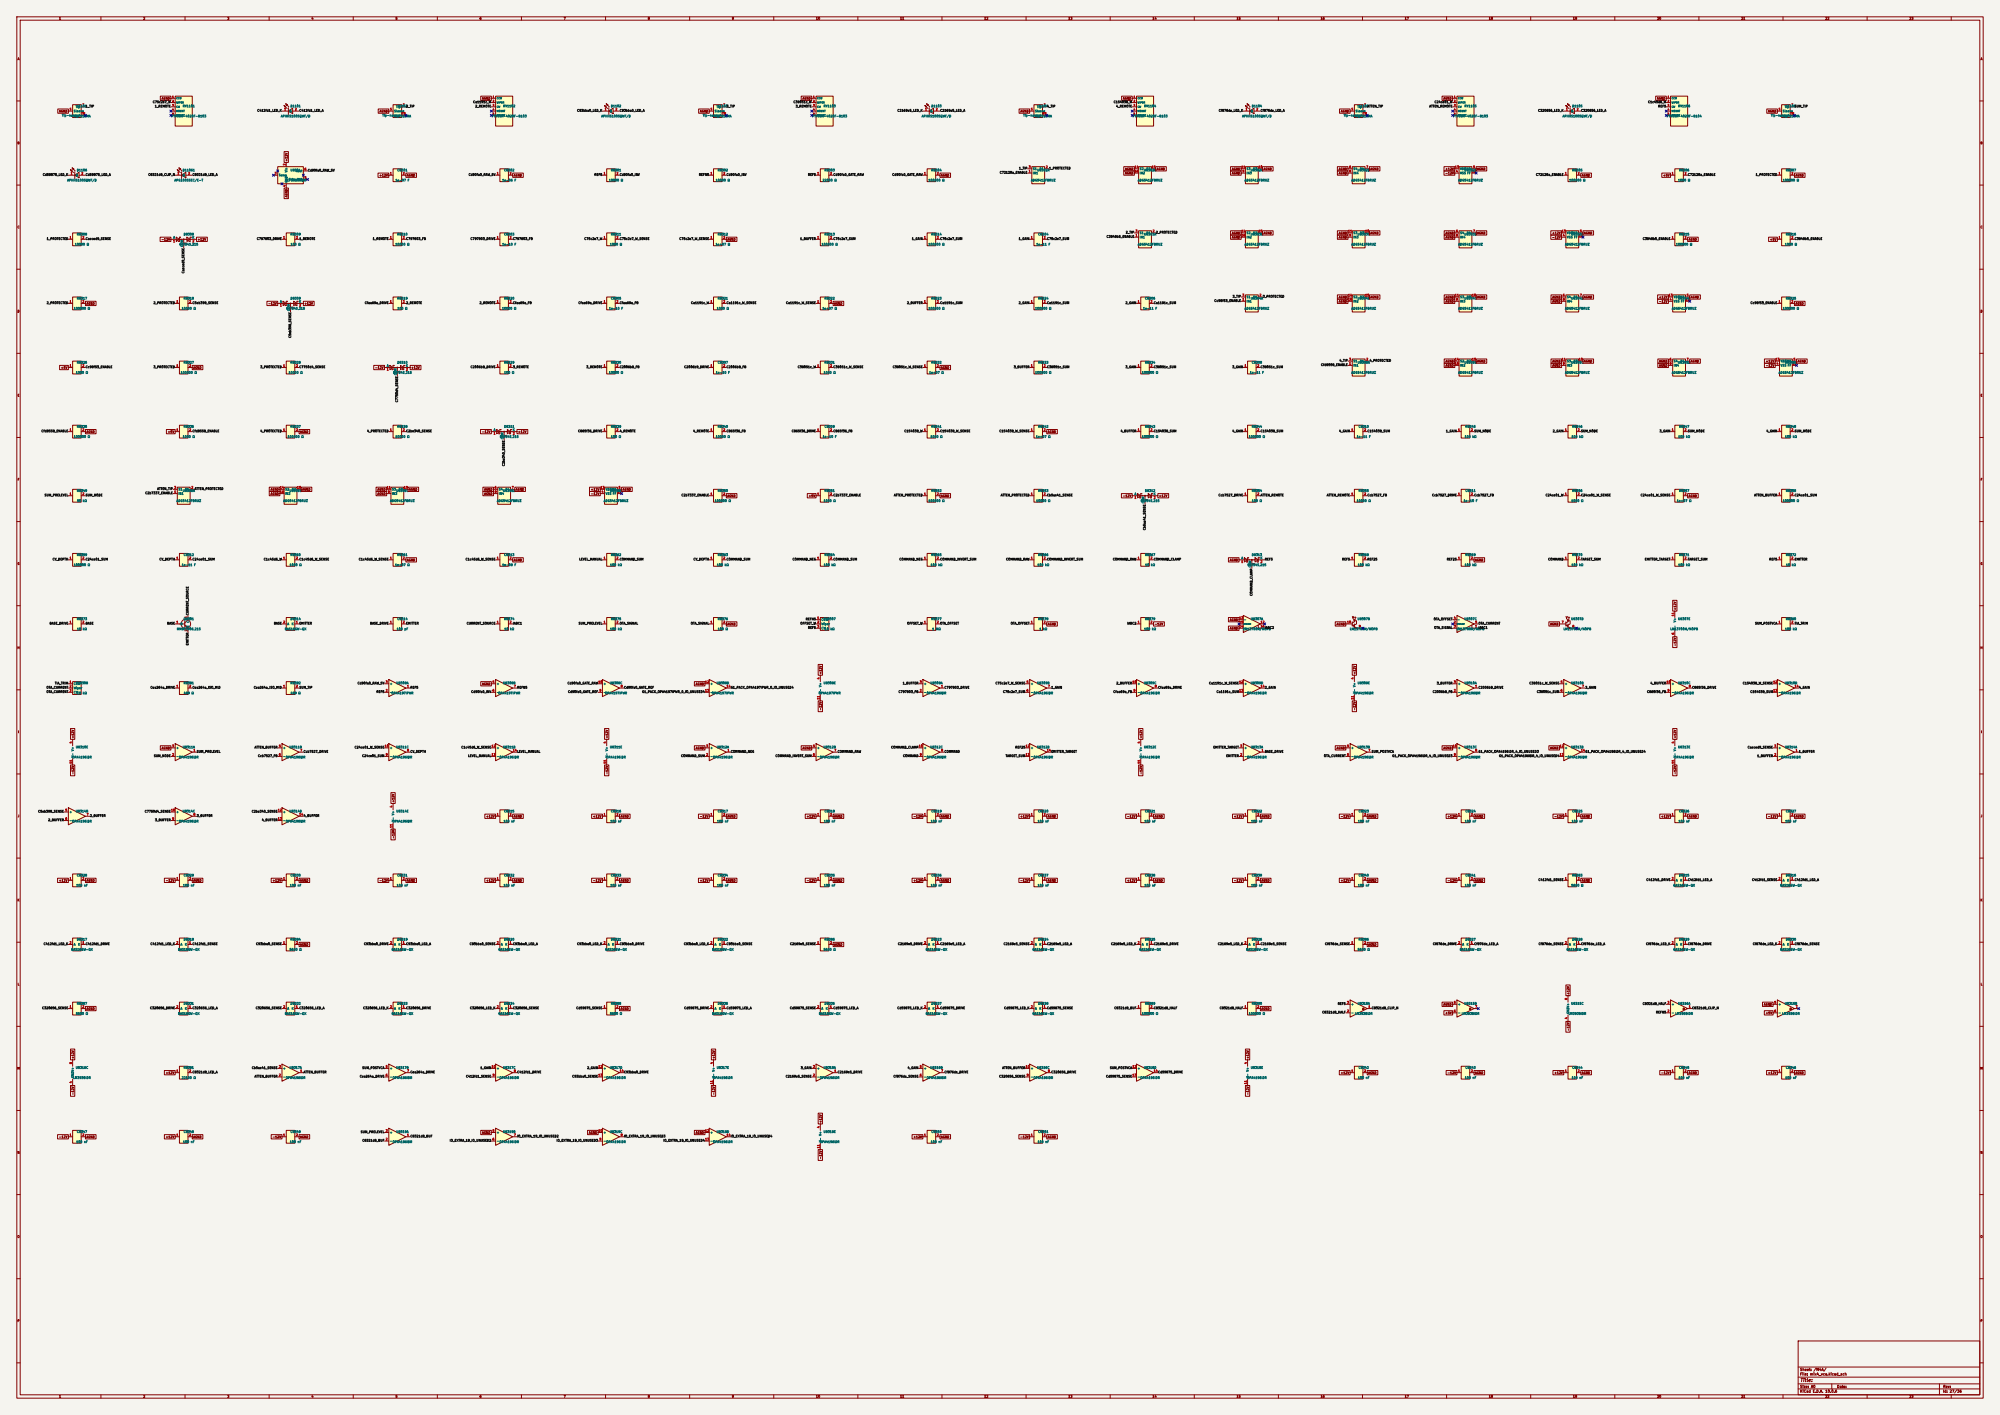
[picture p70: page 27]

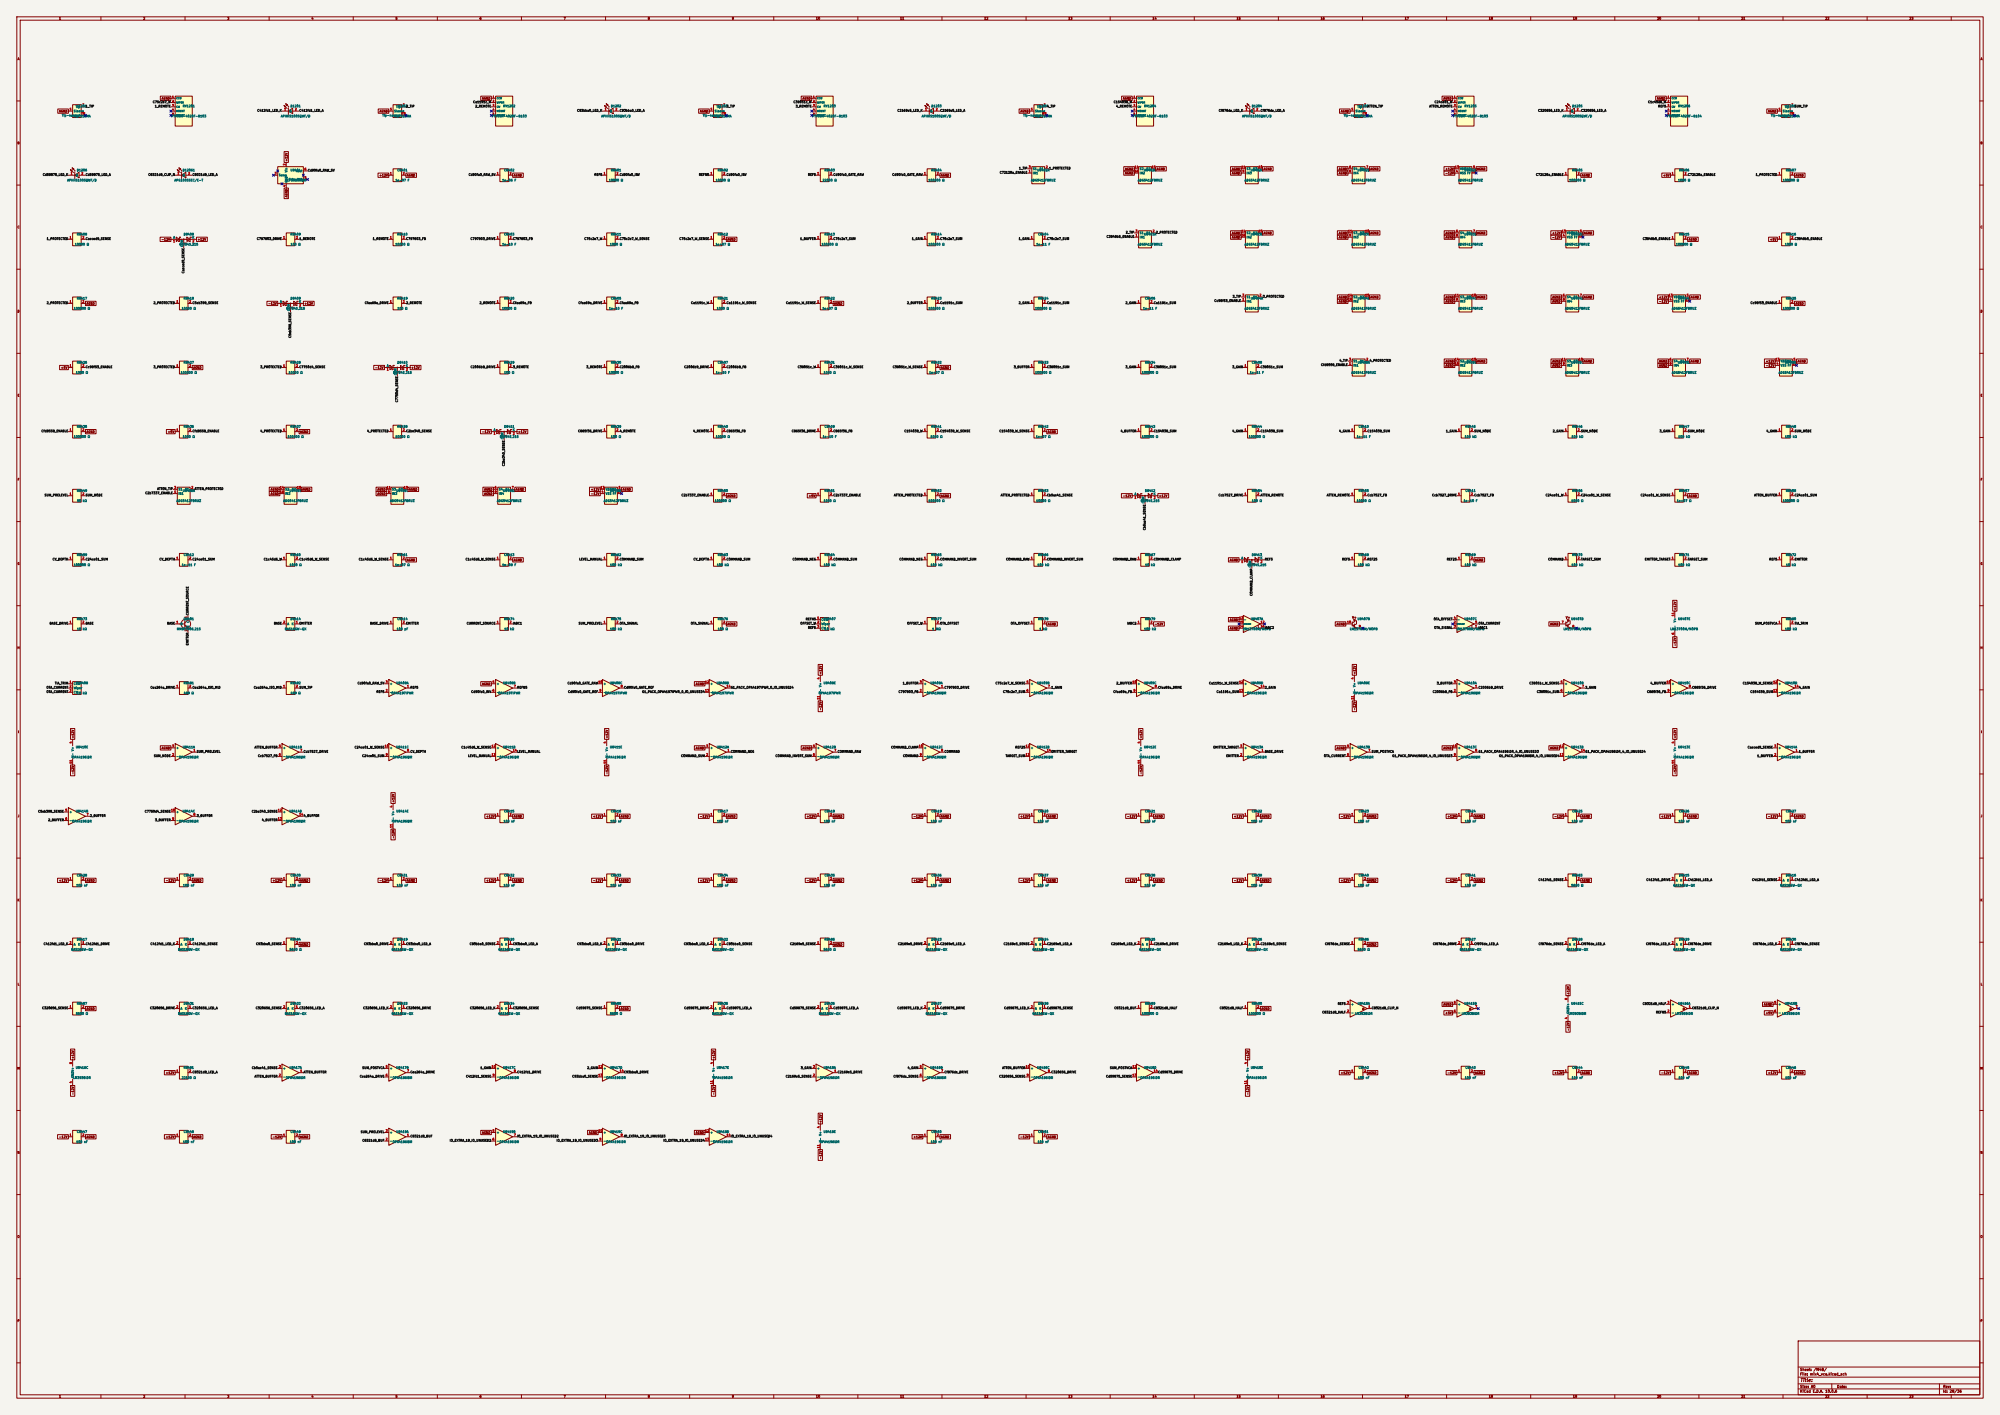
[picture p71: page 28]

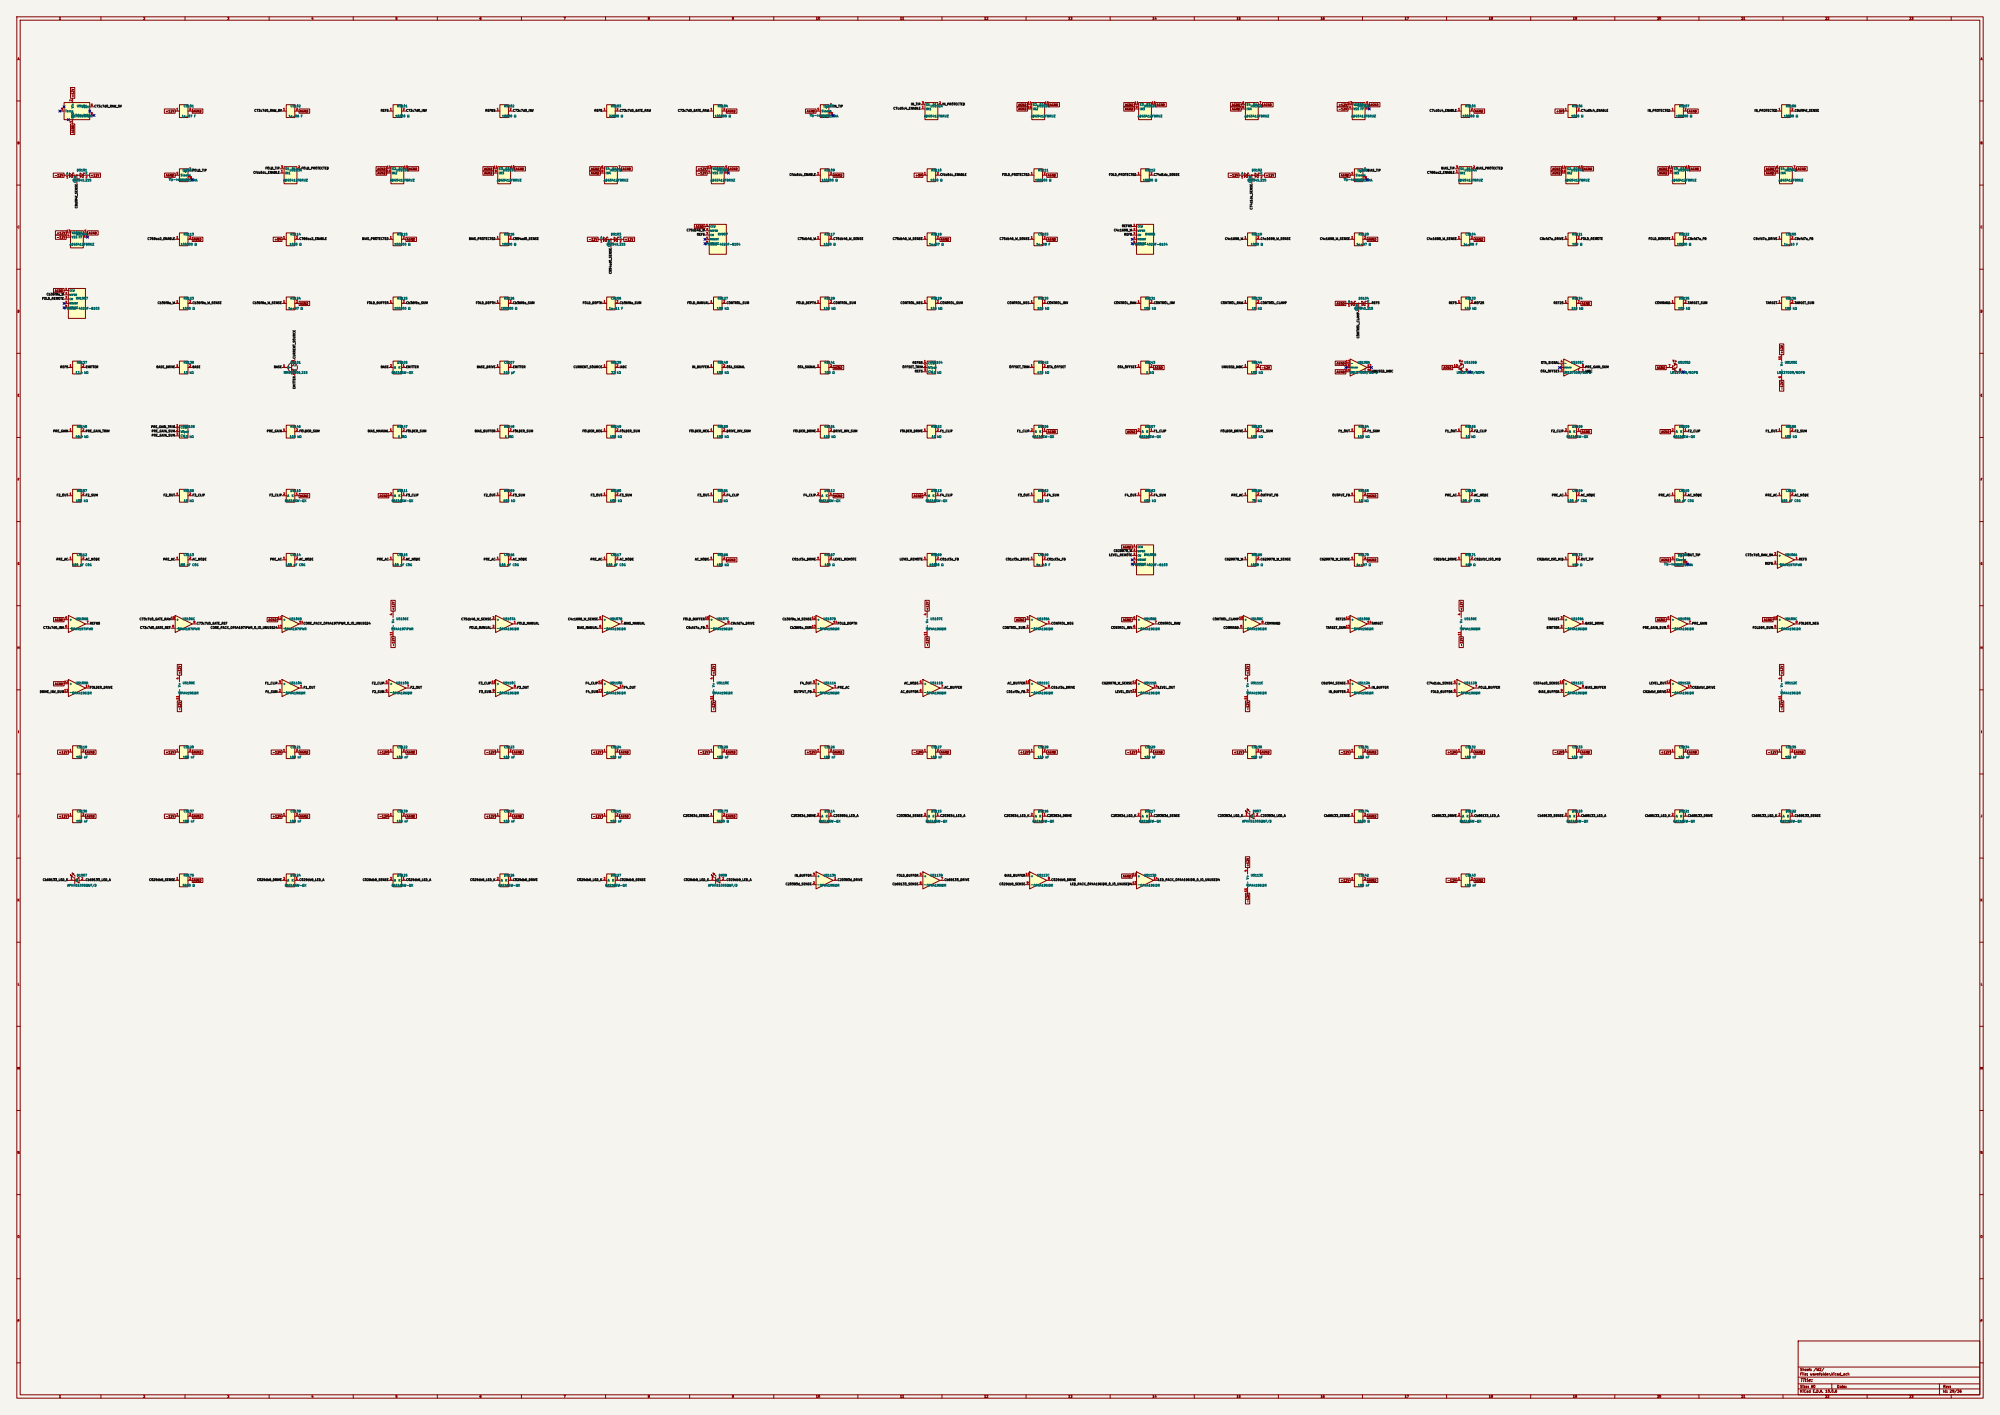
[picture p72: page 29]

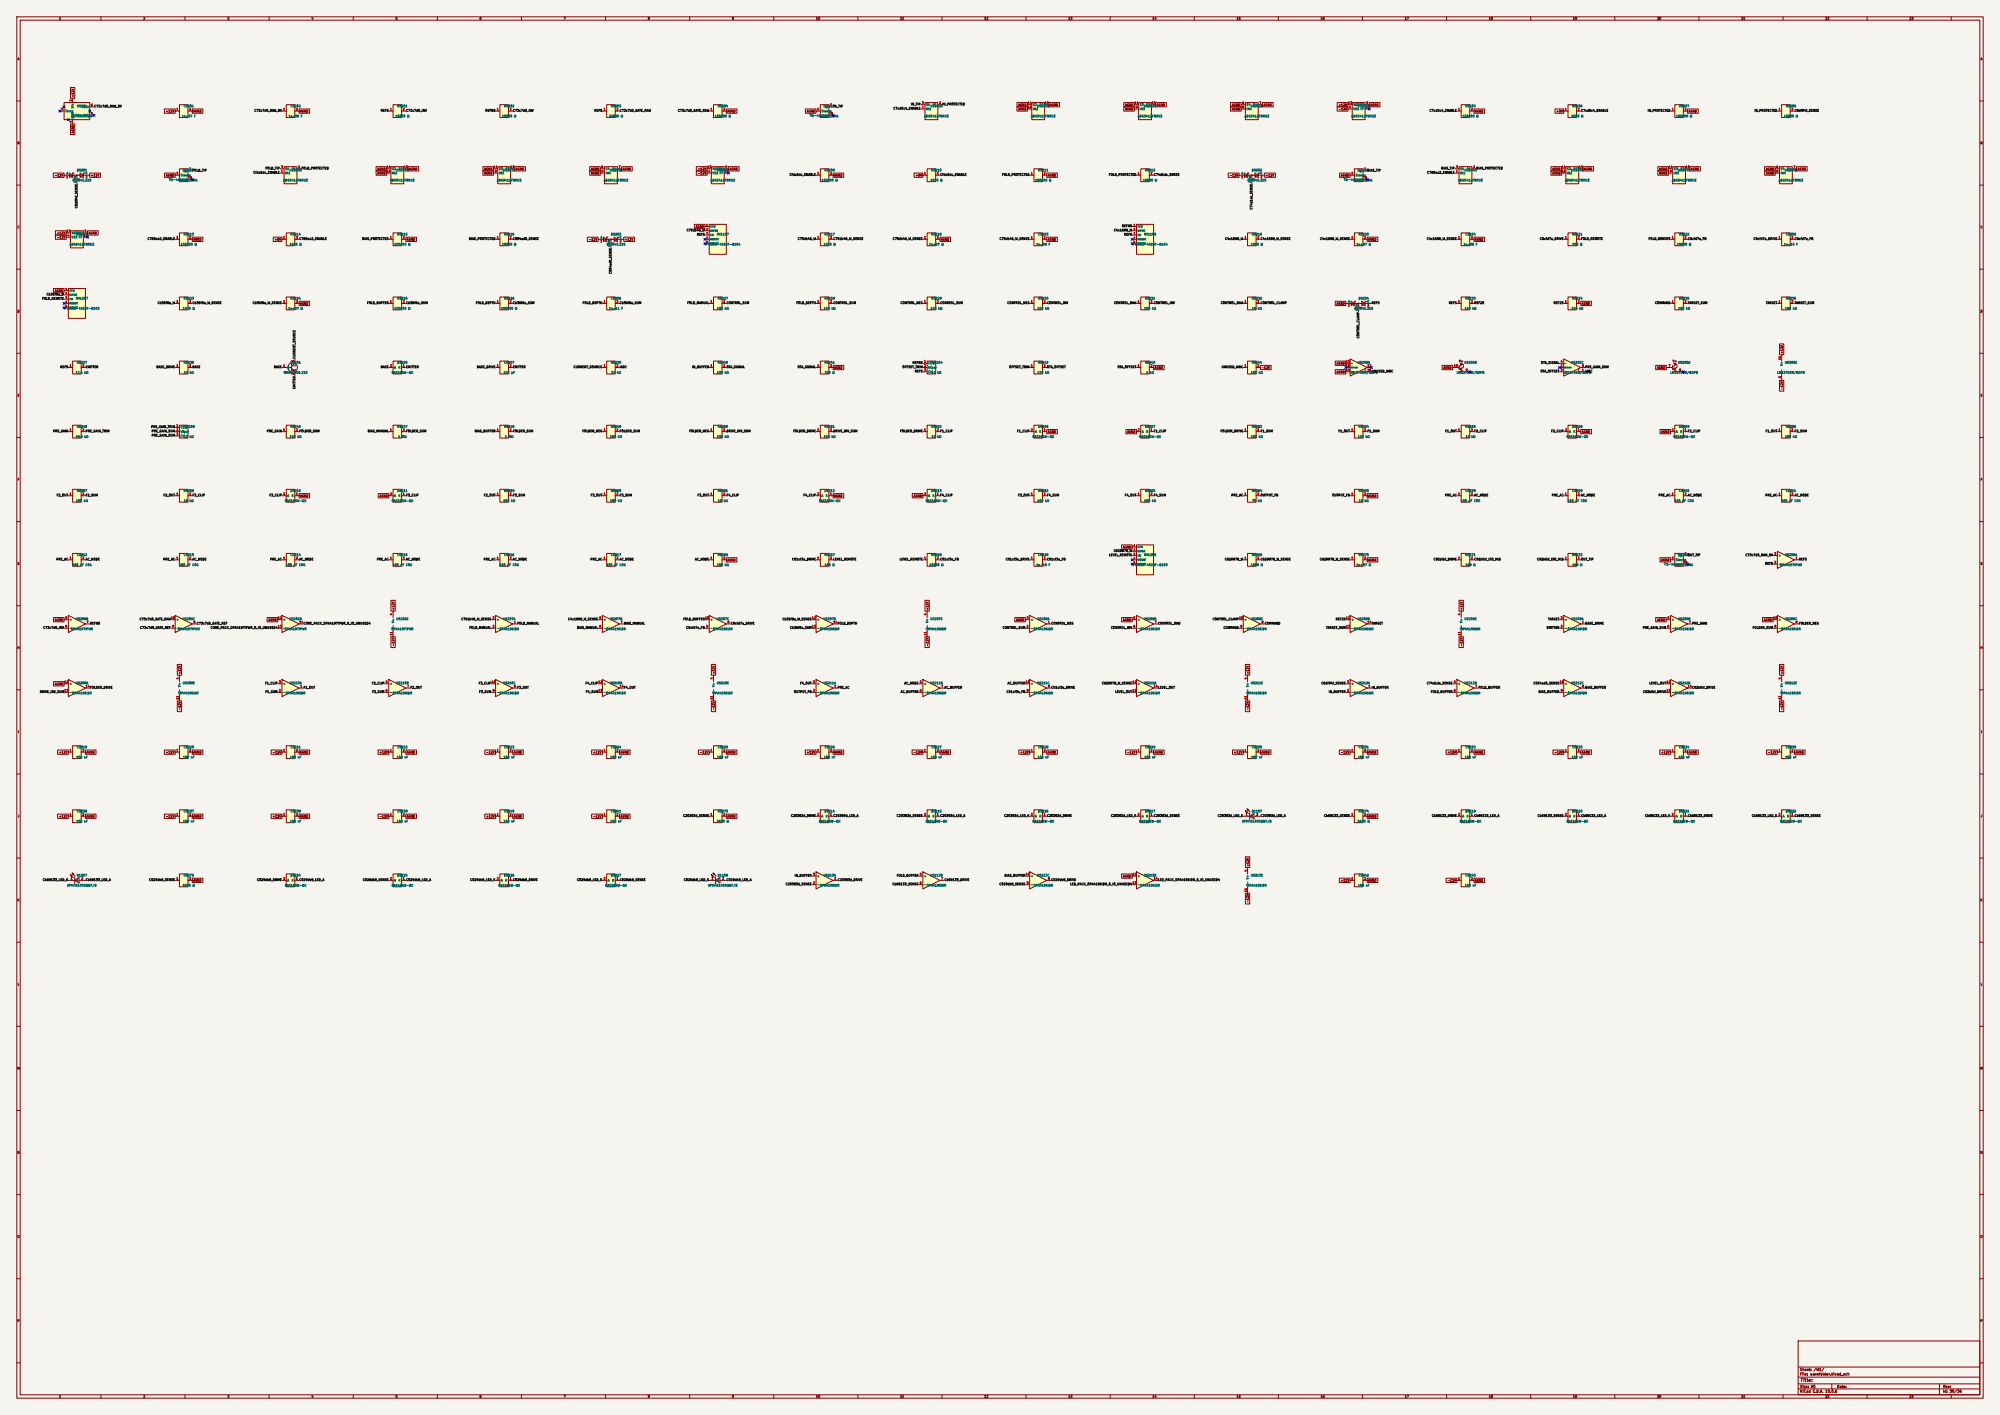
[picture p73: page 30]

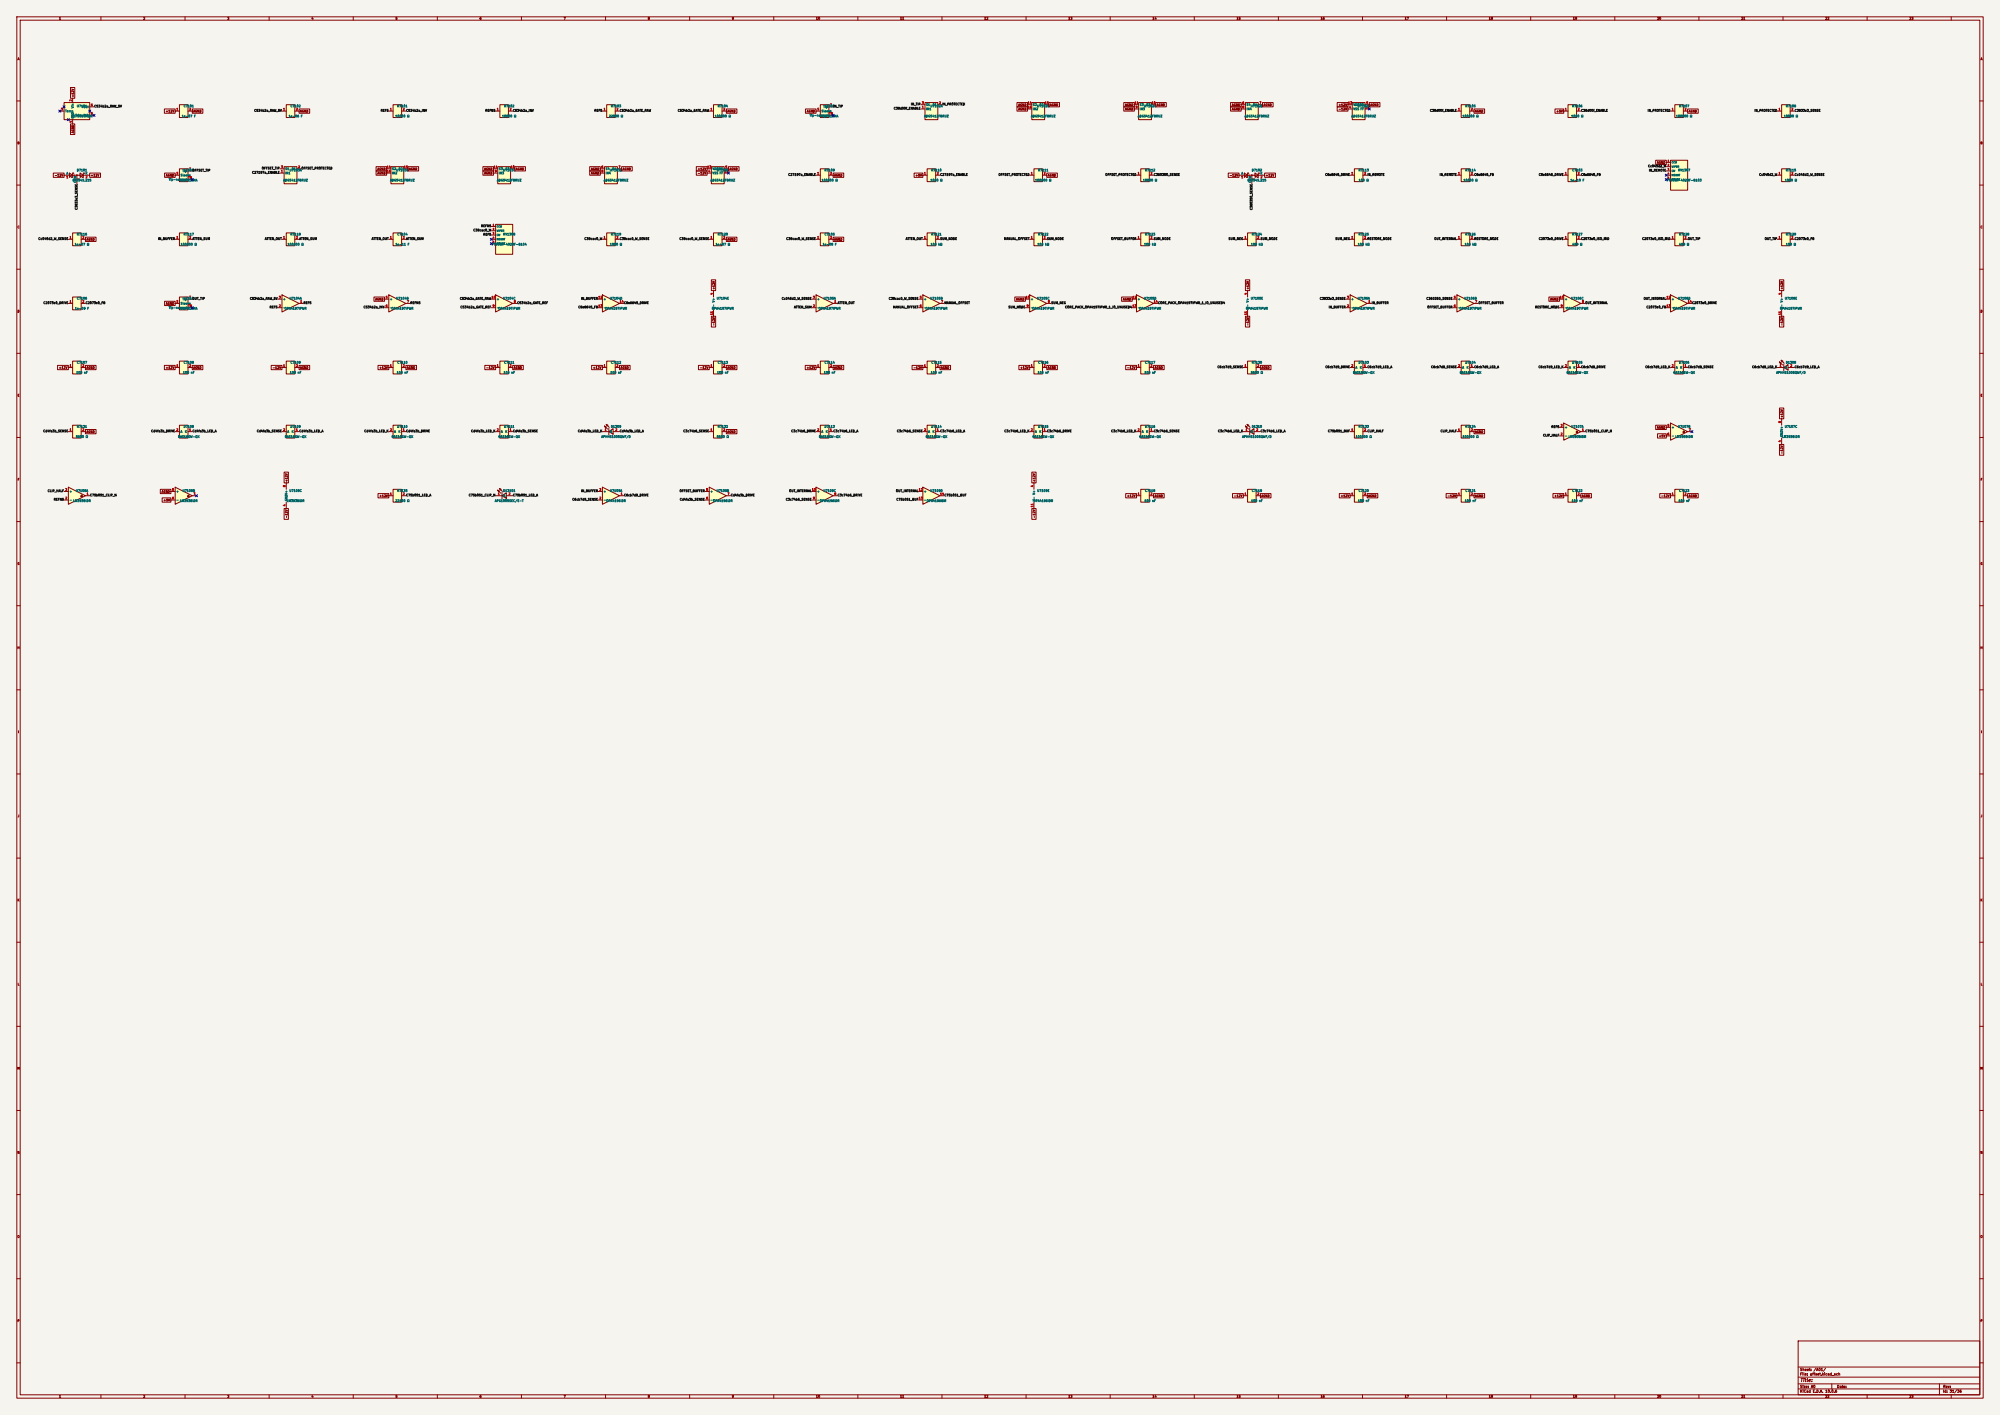
[picture p74: page 31]

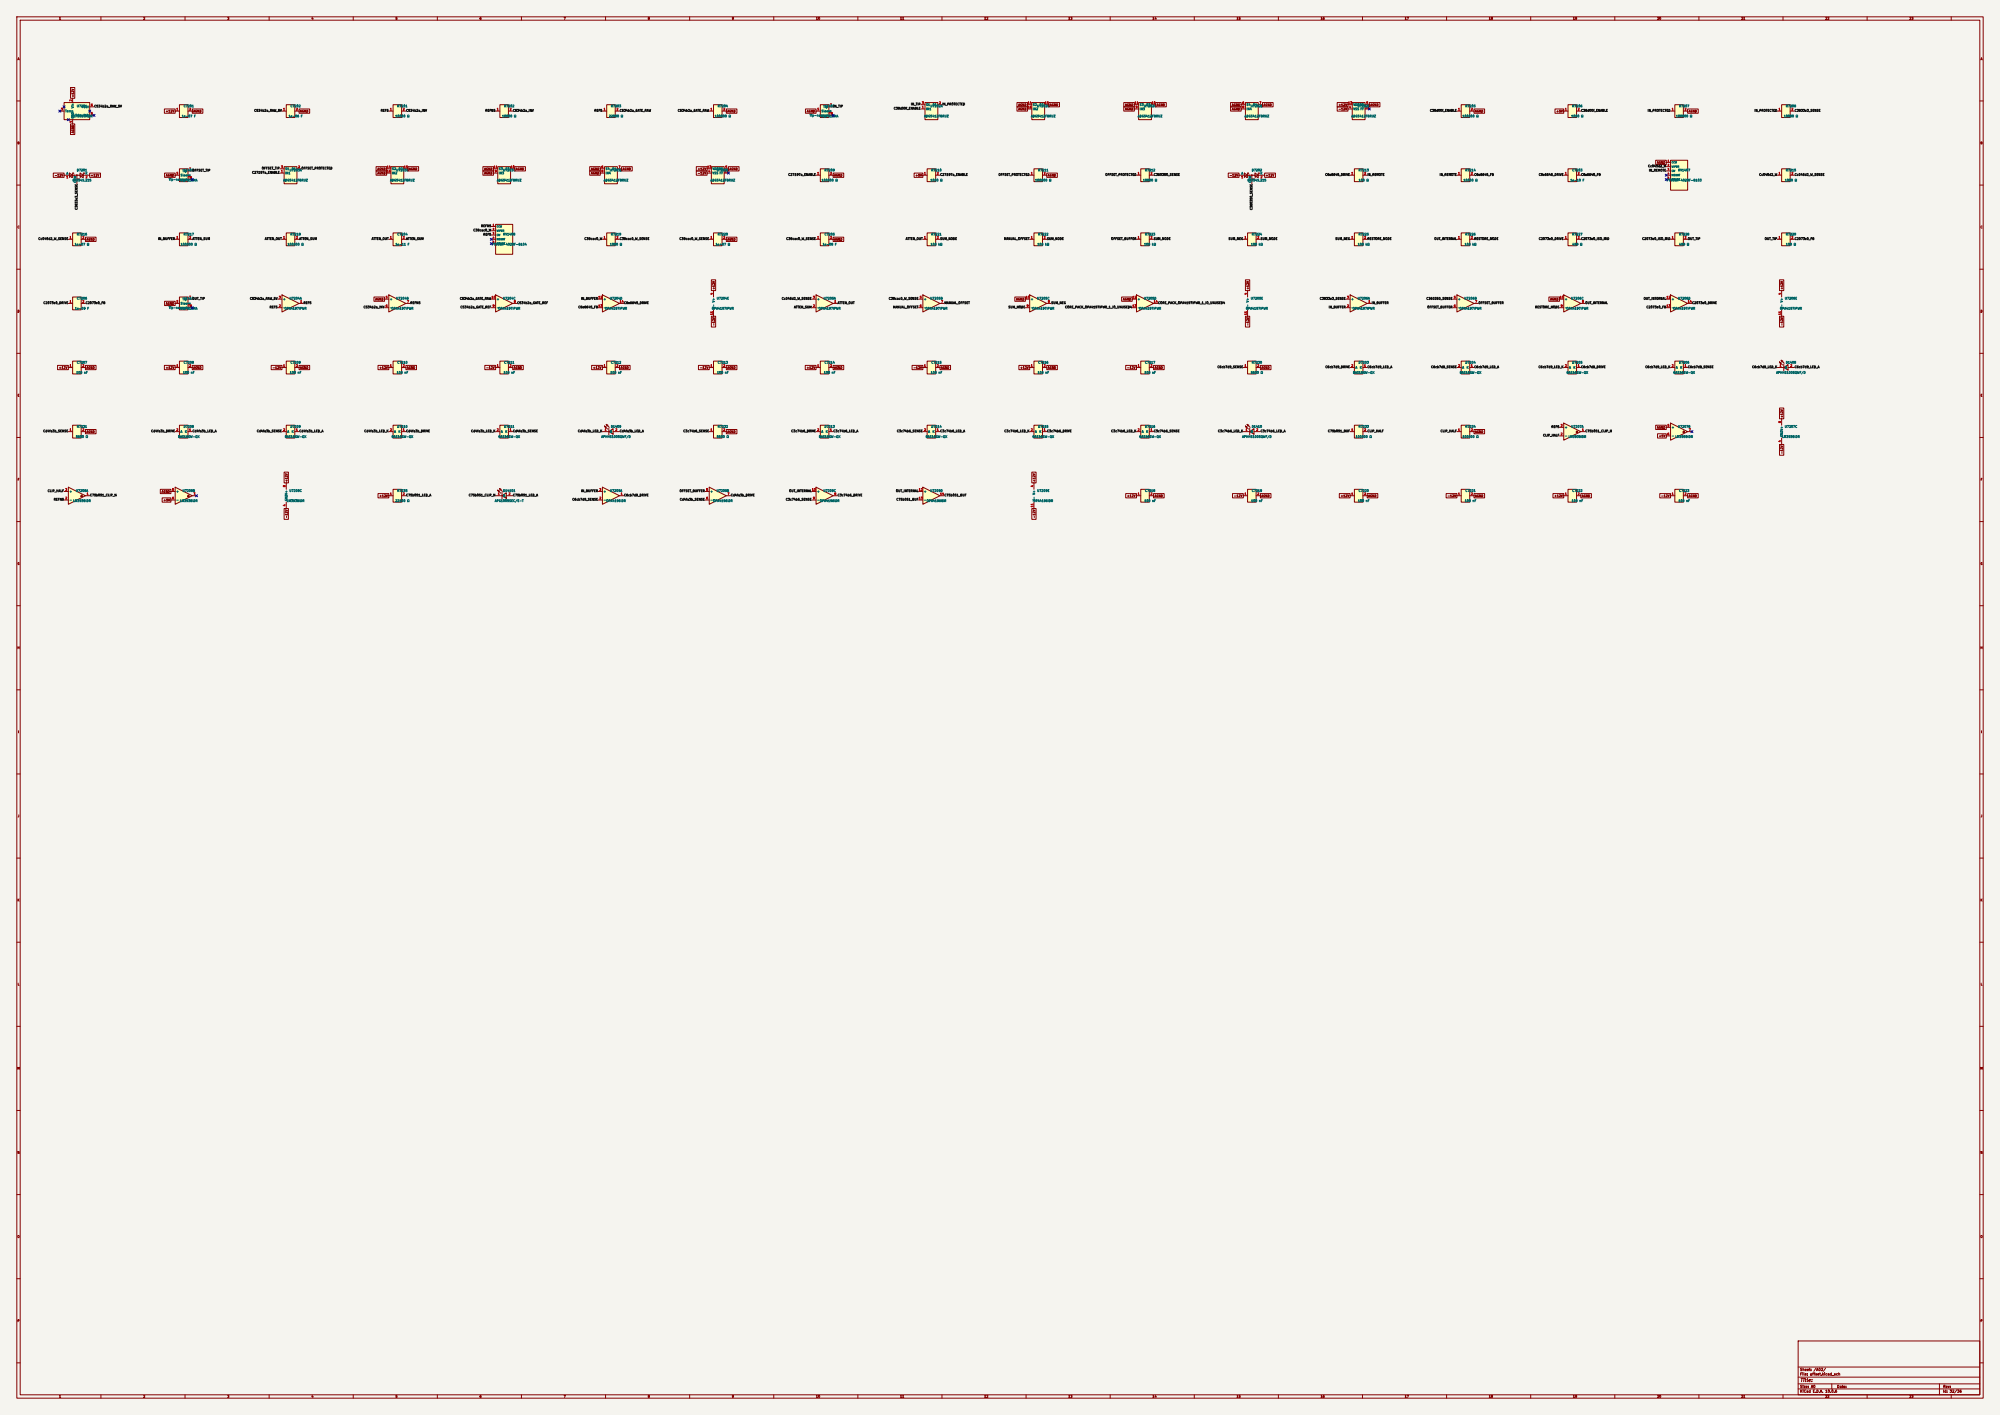
[picture p75: page 32]

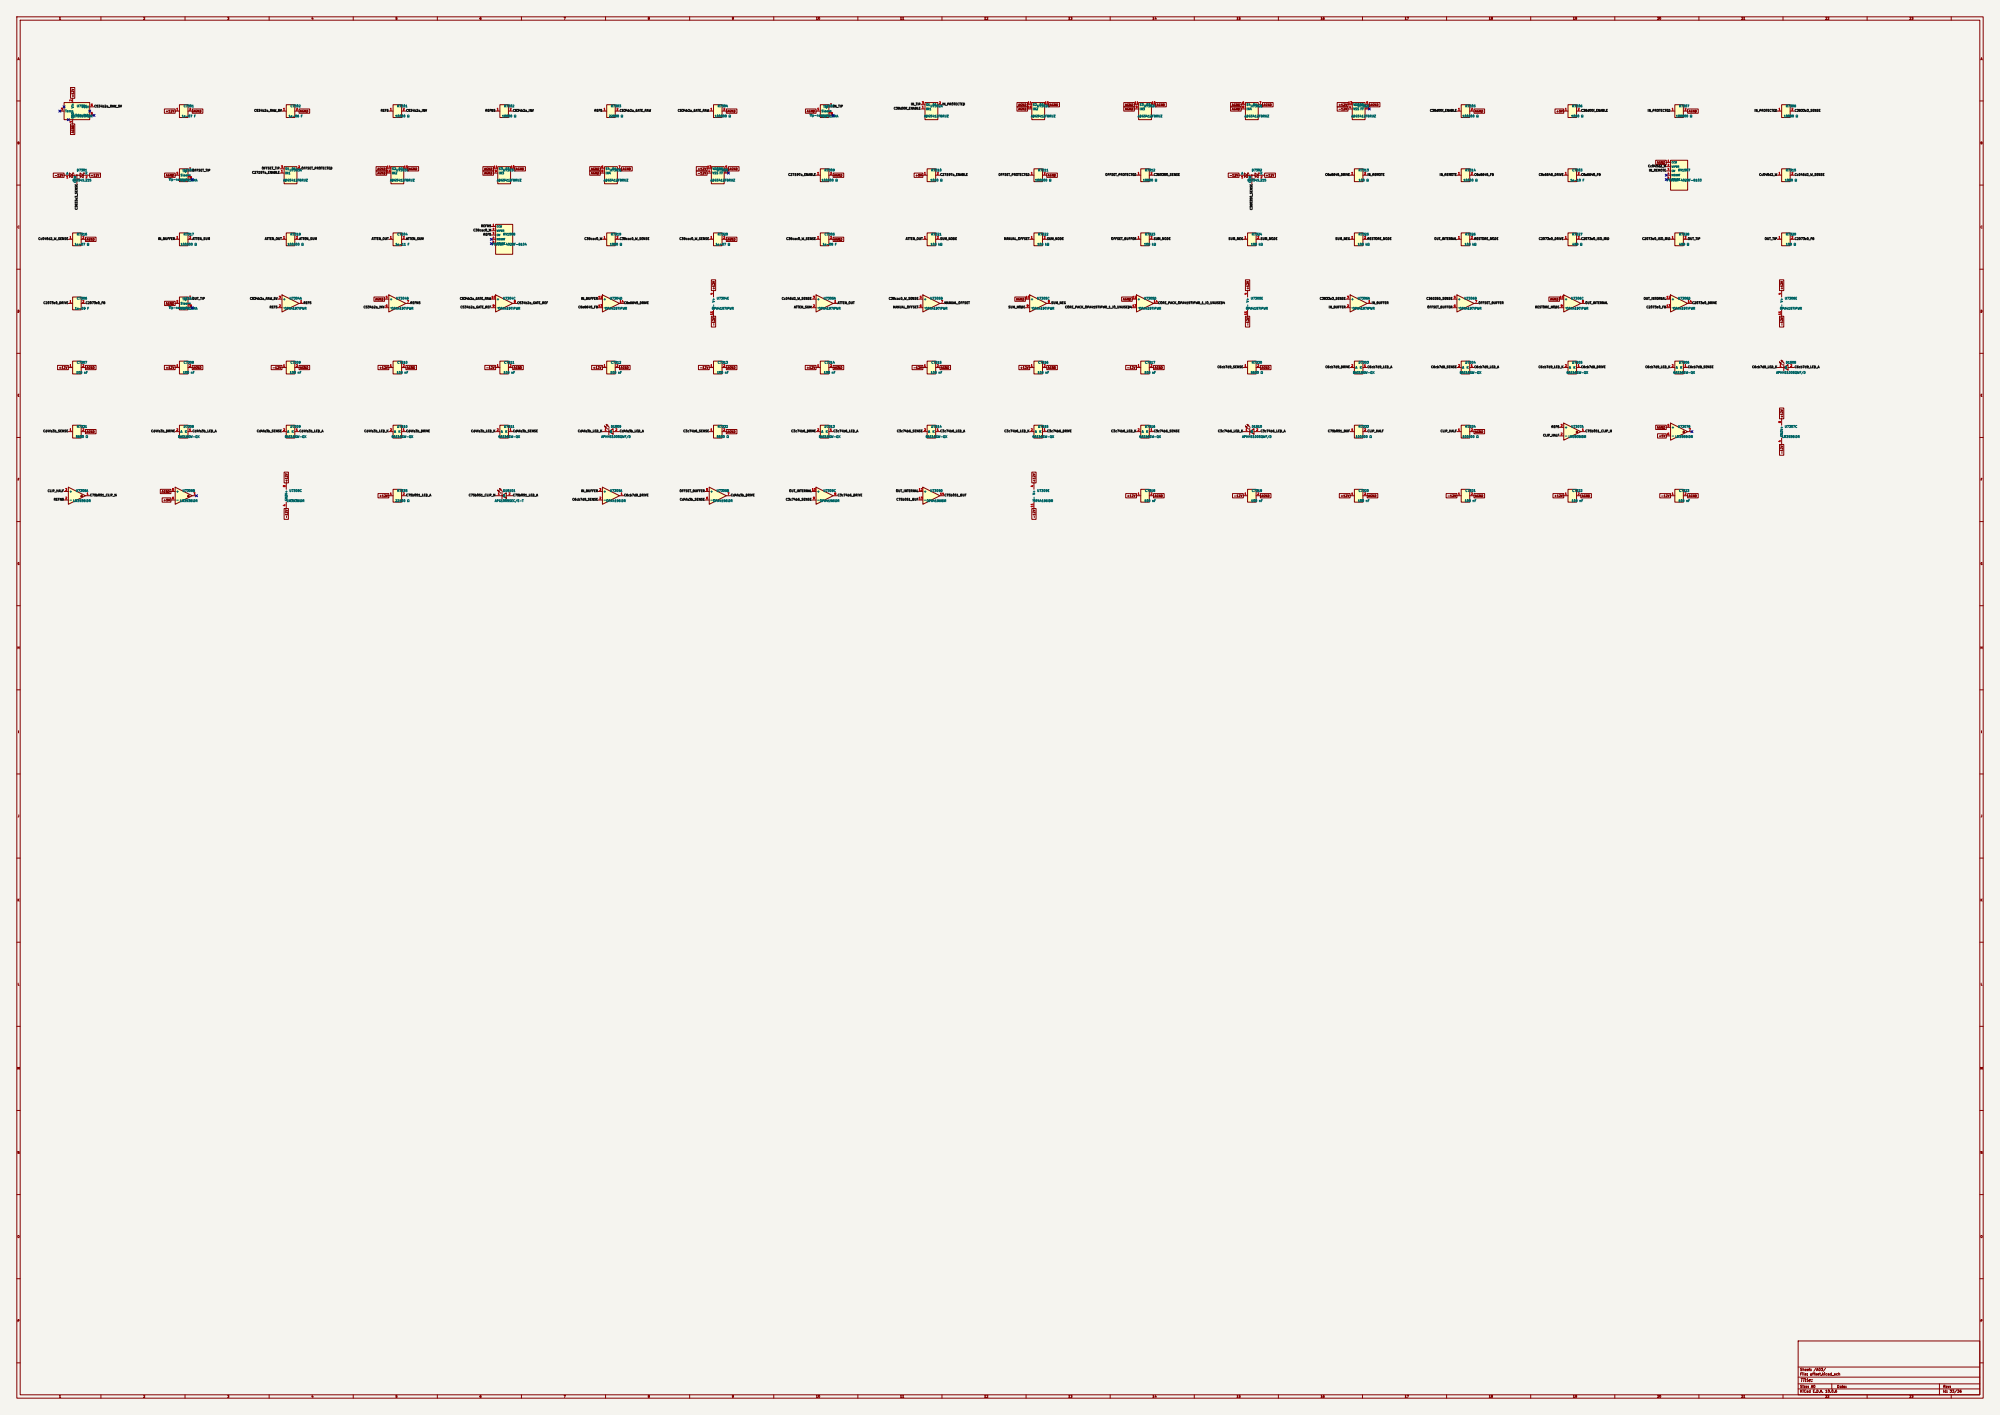
[picture p76: page 33]

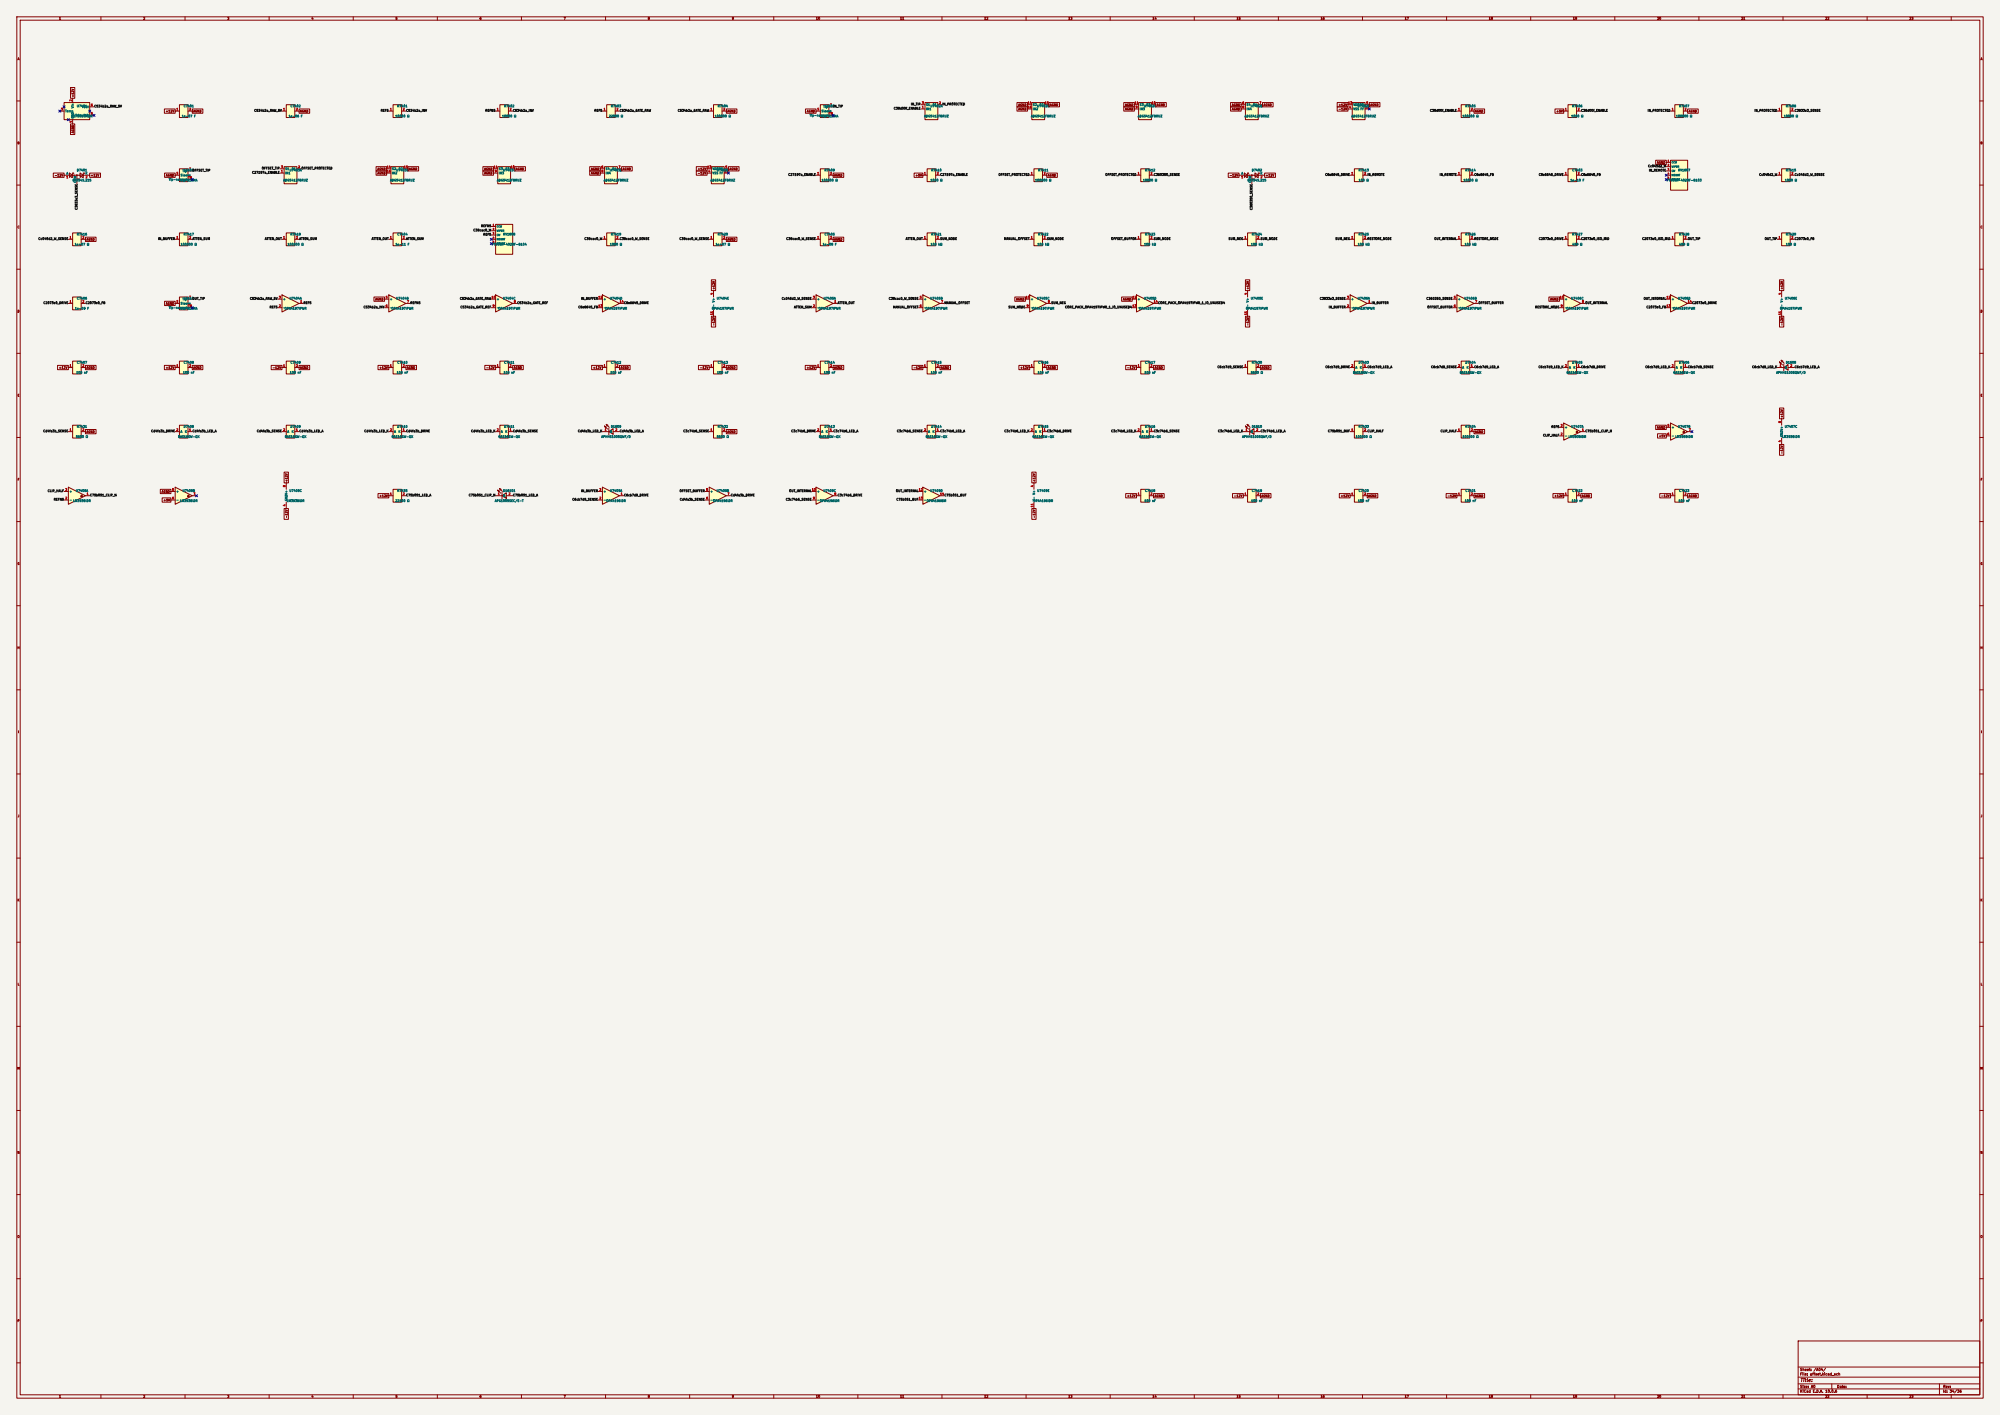
[picture p77: page 34]

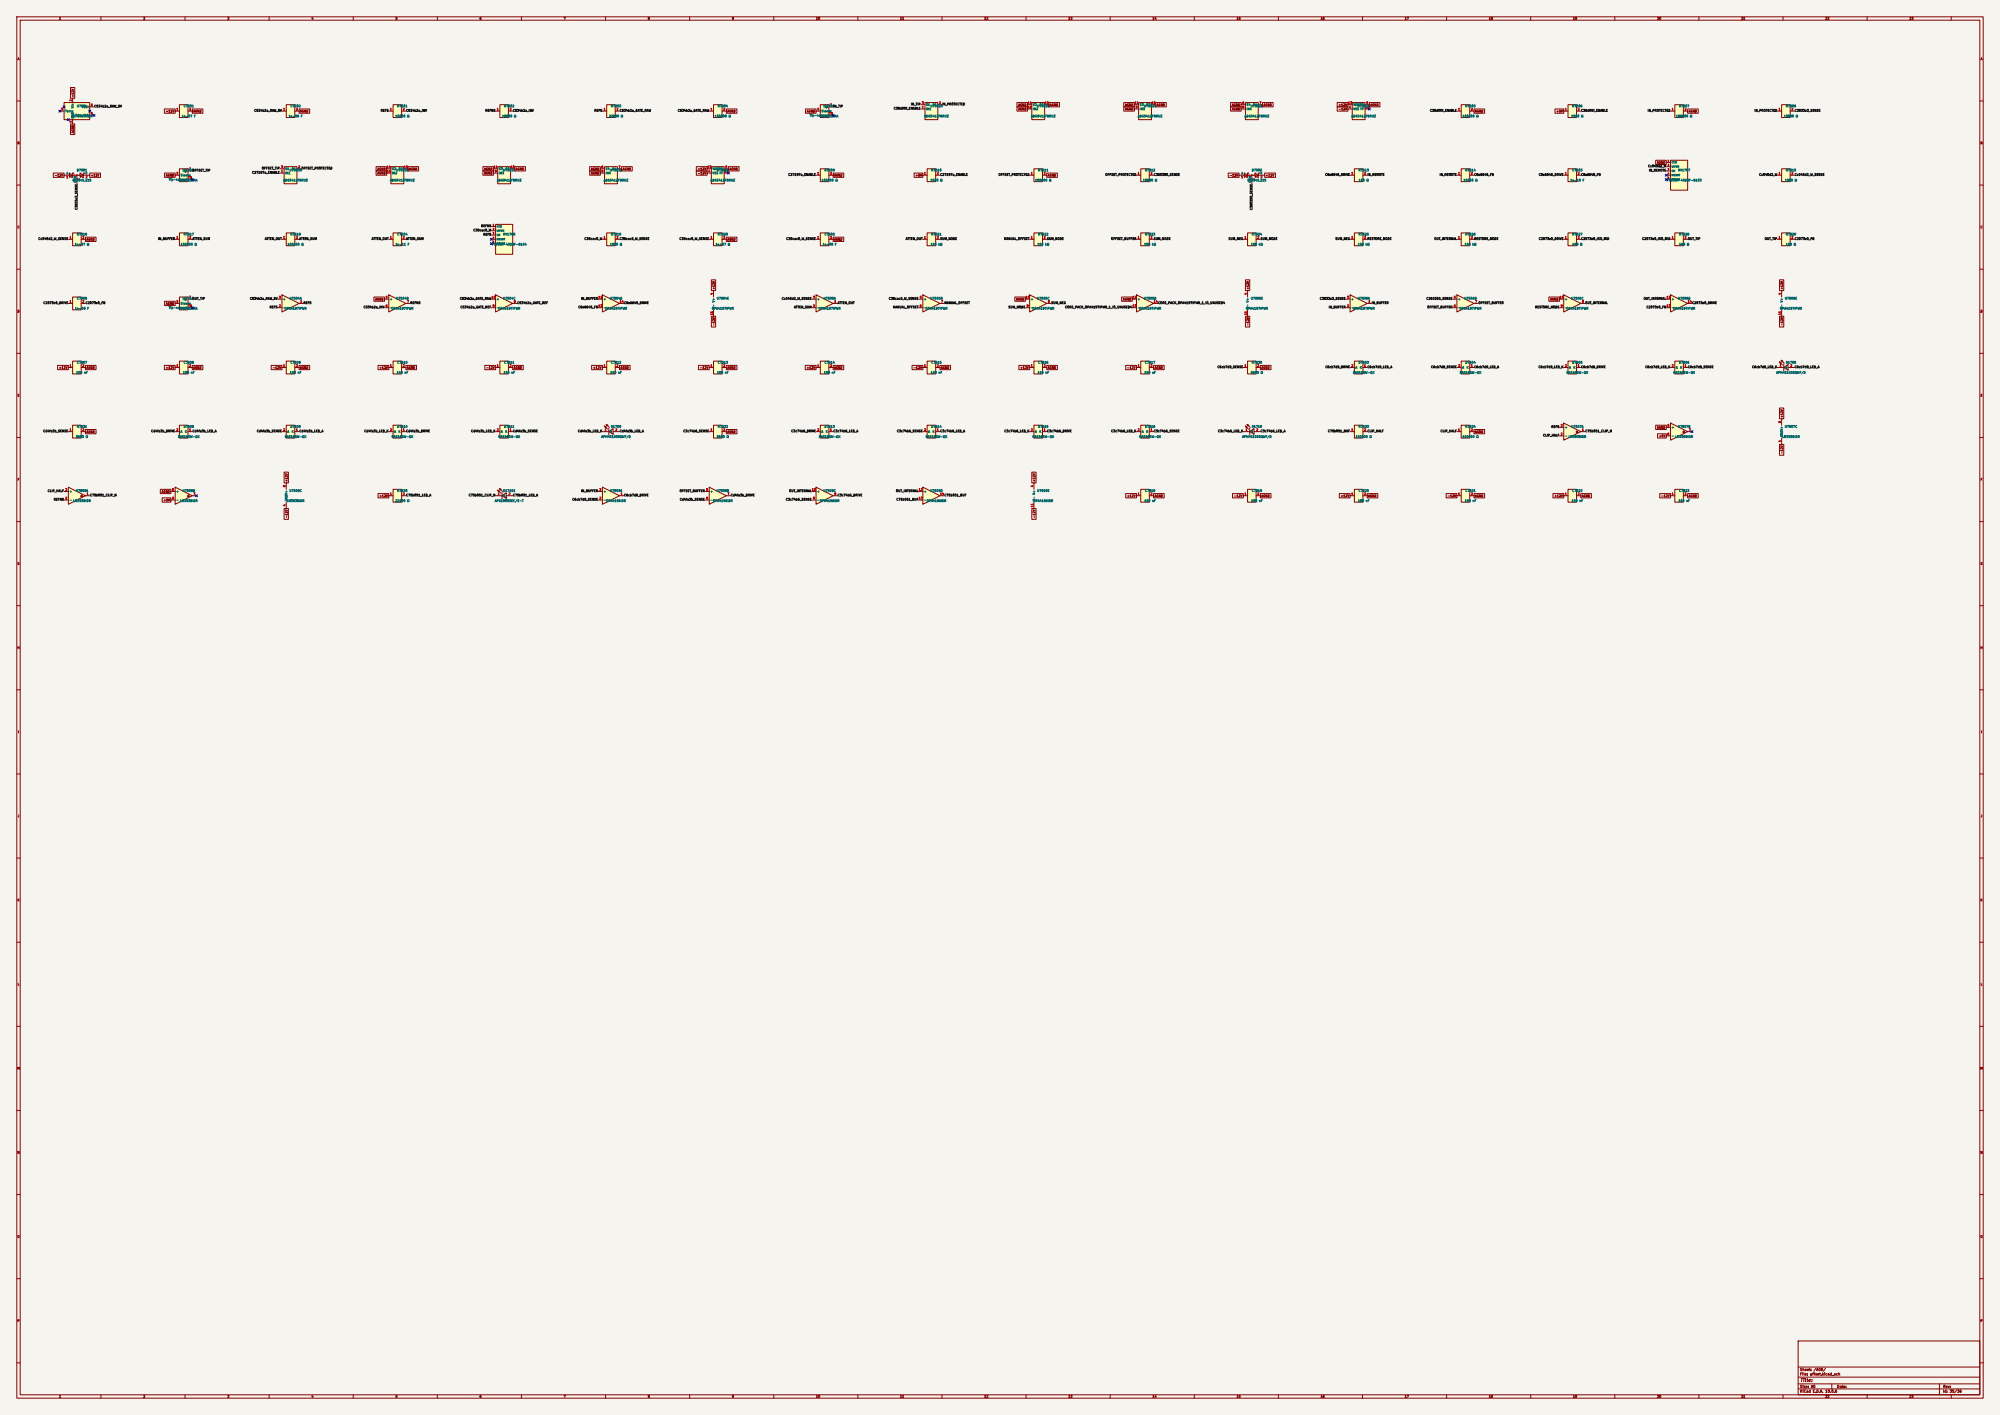
[picture p78: page 35]

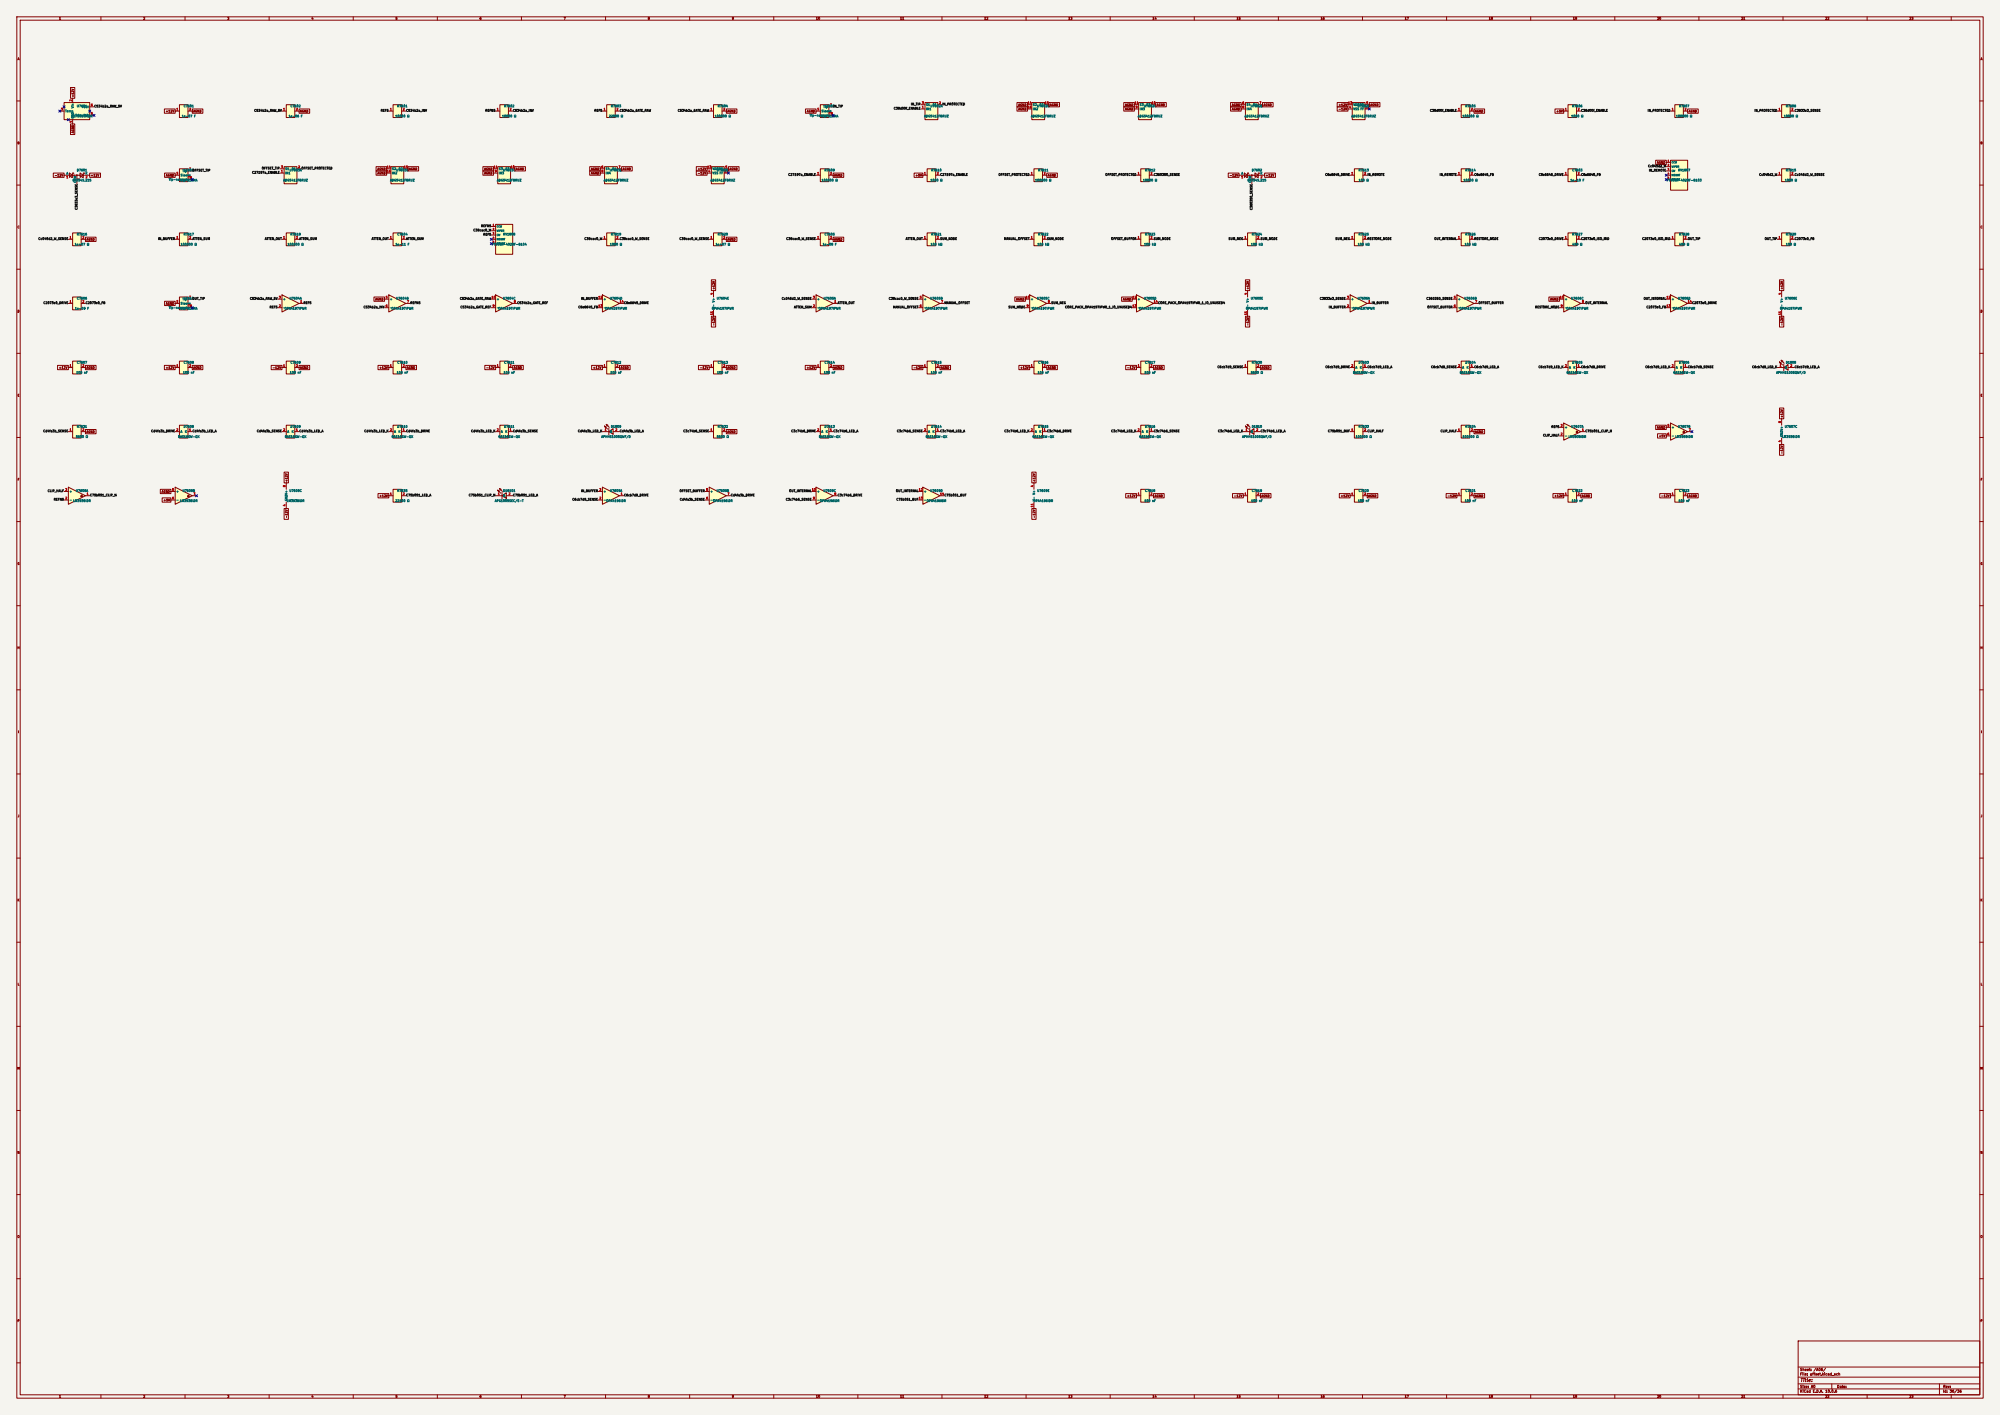
[picture p79: page 36]
