Takazudo/zudo-osc-hole-field/doc/public/assets/osc-hole-field/panel-1to1.pdf

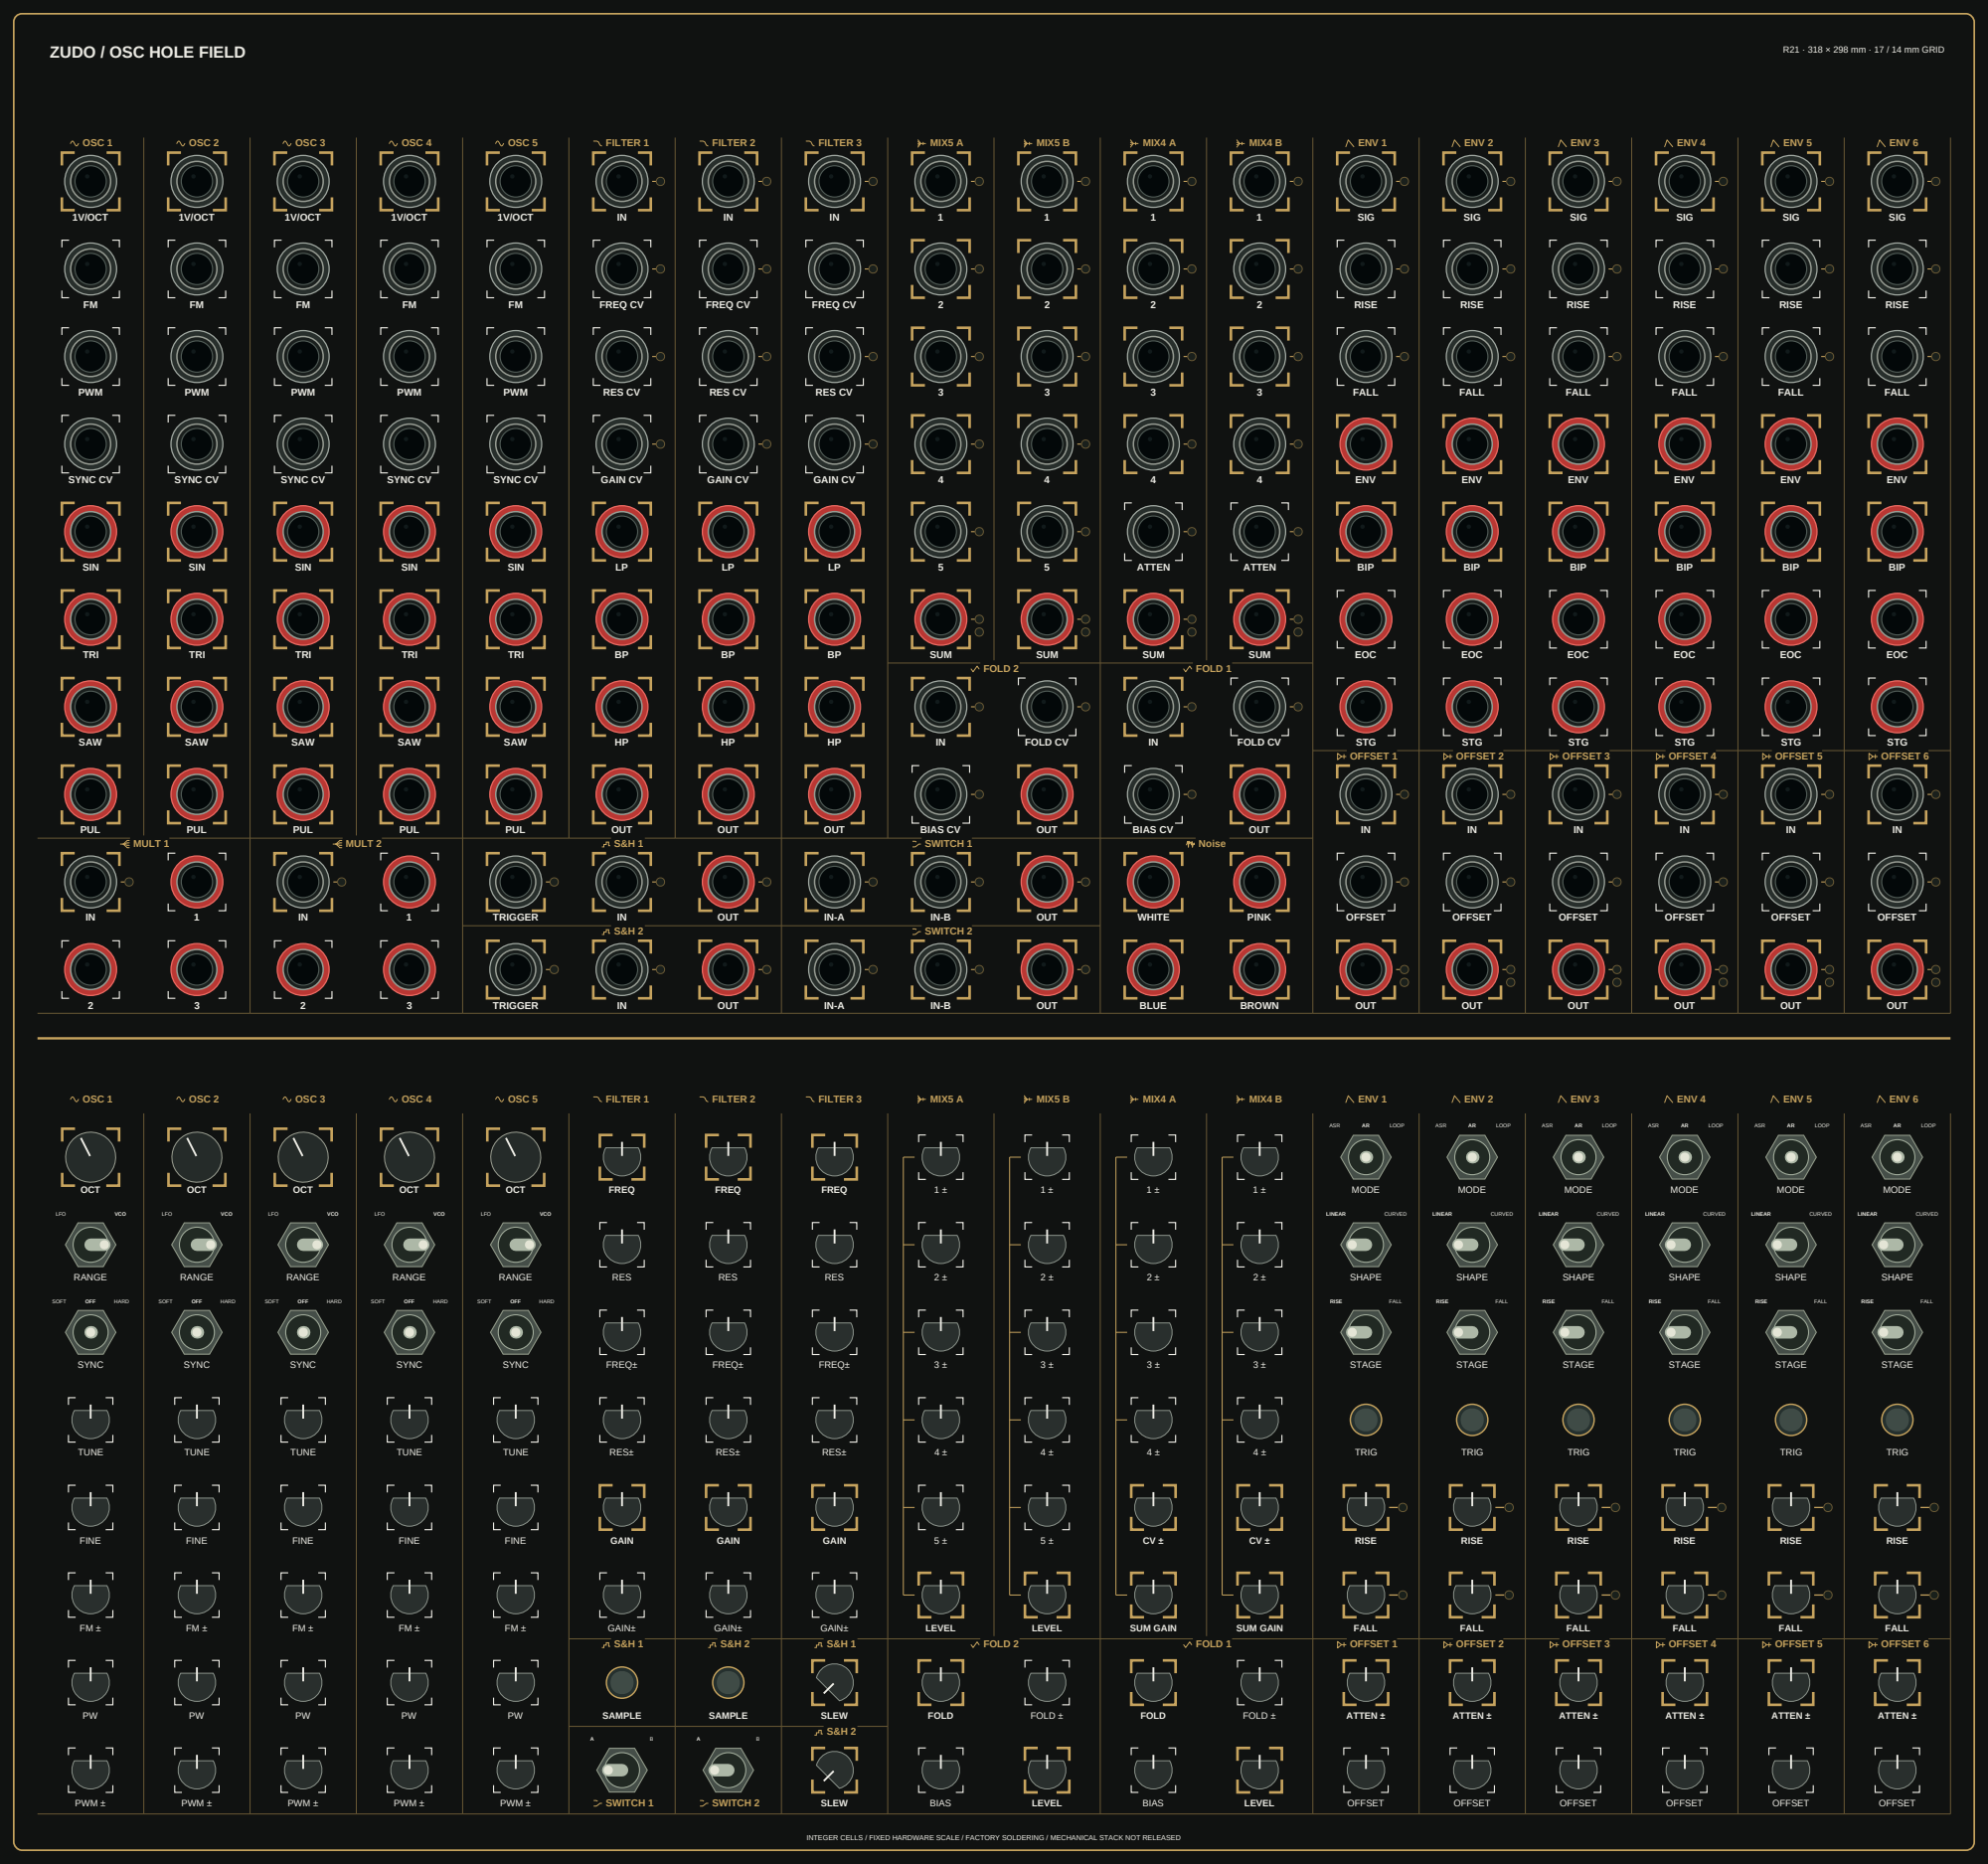
[picture p80: page 1]
ZUDO / OSC HOLE FIELD; R21 · 318 × 298 mm · 17 / 14 mm GRID; OSC 1; OSC 2; OSC 3; OSC 4; OSC 5; FILTER 1; FILTER 2; FILTER 3; MIX5 A; MIX5 B; MIX4 A; MIX4 B; FOLD 2; FOLD 1; ENV 1; OFFSET 1; ENV 2; OFFSET 2; ENV 3; OFFSET 3; ENV 4; OFFSET 4; ENV 5; OFFSET 5; ENV 6; OFFSET 6; MULT 1; MULT 2; SWITCH 1; SWITCH 2; Noise; 1V/OCT; PWM; SYNC CV; SIN; TRI; SAW; PUL; FREQ CV; RES CV; GAIN CV; OUT; SUM; ATTEN; FOLD CV; BIAS CV; SIG; RISE; FALL; ENV; BIP; EOC; STG; OFFSET; TRIGGER; WHITE; PINK; BLUE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

INTEGER CELLS / FIXED HARDWARE SCALE / FACTORY SOLDERING / MECHANICAL STACK NOT RELEASED
