Takazudo/zudo-osc-hole-field/circuit/sources/toggle-button/DW2-2MS3T1B1M2QES.pdf

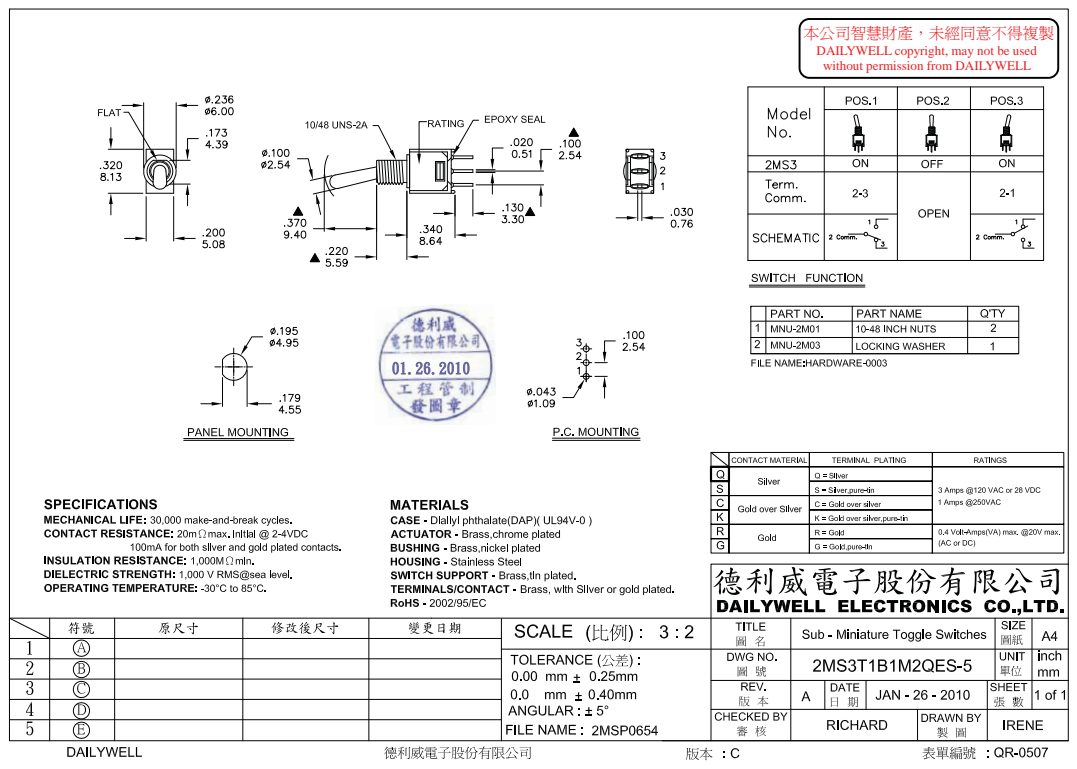
[picture p81: page 1]

DAILYWELL copyright, may not be used
without permission from DAILYWELL

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

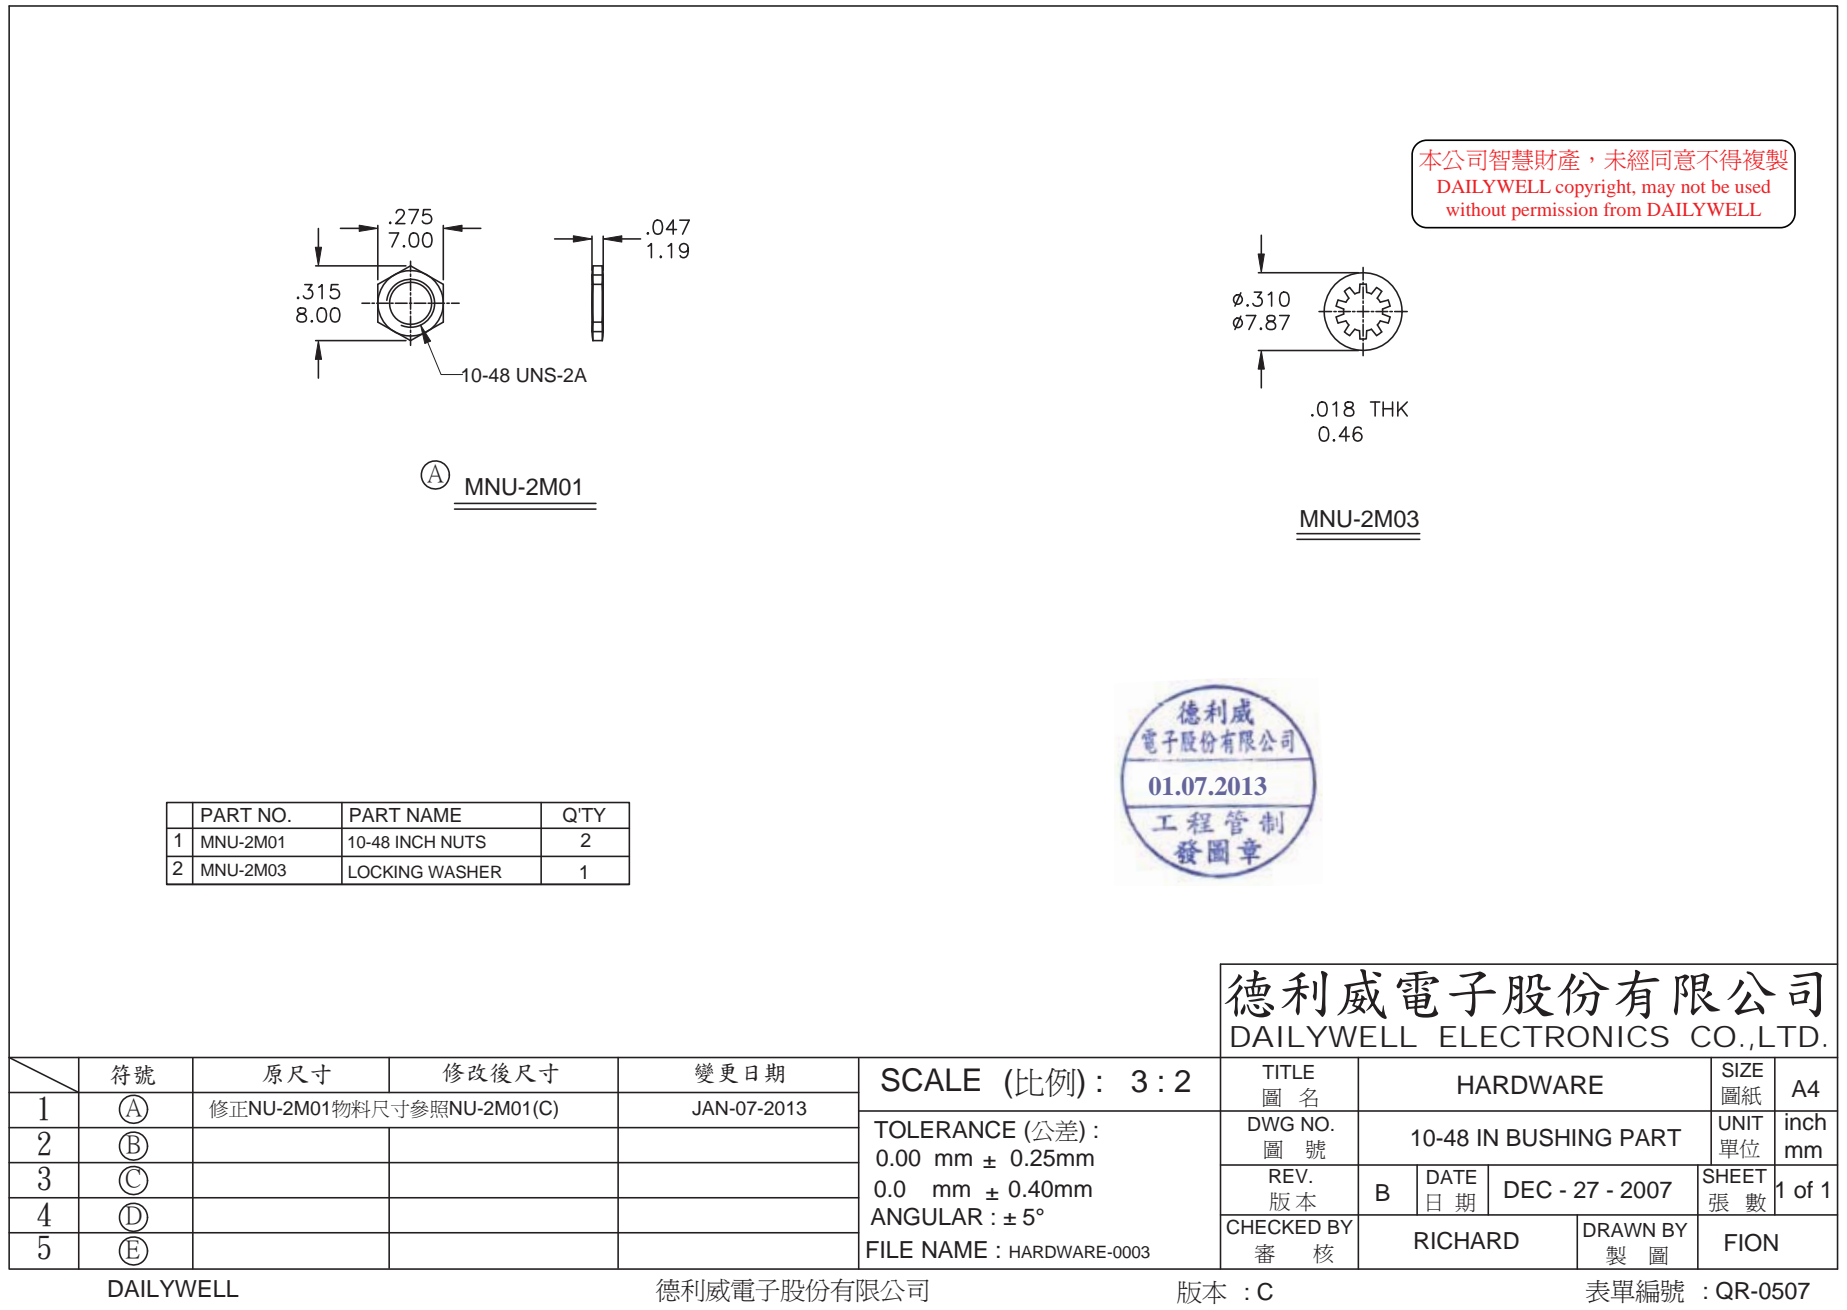
[picture p82: page 2]
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
