Takazudo/zudo-osc-hole-field/design/spec/cells/spice/precision-output-sweep.cir

OSC-ES-1 dual feedback diagnostic; ideal zero-delay 100000 V/V source, not OPA4197

Vsig1 sig1 0 PULSE(-5 5 0 1u 1u 500u 1m)
Eamp1 drive1 0 sig1 fb1 1e5
Risoa1 drive1 mid1 499
Risob1 mid1 jack1 499
Rfb1 jack1 fb1 10k
Cfast1 drive1 fb1 100p
Rload1 jack1 0 1e+12
Vsig2 sig2 0 PULSE(-5 5 0 1u 1u 500u 1m)
Eamp2 drive2 0 sig2 fb2 1e5
Risoa2 drive2 mid2 499
Risob2 mid2 jack2 499
Rfb2 jack2 fb2 10k
Cfast2 drive2 fb2 100p
Rload2 jack2 0 1e+12
Cload2 jack2 0 1e-10
Vsig3 sig3 0 PULSE(-5 5 0 1u 1u 500u 1m)
Eamp3 drive3 0 sig3 fb3 1e5
Risoa3 drive3 mid3 499
Risob3 mid3 jack3 499
Rfb3 jack3 fb3 10k
Cfast3 drive3 fb3 100p
Rload3 jack3 0 1e+12
Cload3 jack3 0 1e-09
Vsig4 sig4 0 PULSE(-5 5 0 1u 1u 500u 1m)
Eamp4 drive4 0 sig4 fb4 1e5
Risoa4 drive4 mid4 499
Risob4 mid4 jack4 499
Rfb4 jack4 fb4 10k
Cfast4 drive4 fb4 100p
Rload4 jack4 0 1e+12
Cload4 jack4 0 5e-09
Vsig5 sig5 0 PULSE(-5 5 0 1u 1u 500u 1m)
Eamp5 drive5 0 sig5 fb5 1e5
Risoa5 drive5 mid5 499
Risob5 mid5 jack5 499
Rfb5 jack5 fb5 10k
Cfast5 drive5 fb5 100p
Rload5 jack5 0 100000
Vsig6 sig6 0 PULSE(-5 5 0 1u 1u 500u 1m)
Eamp6 drive6 0 sig6 fb6 1e5
Risoa6 drive6 mid6 499
Risob6 mid6 jack6 499
Rfb6 jack6 fb6 10k
Cfast6 drive6 fb6 100p
Rload6 jack6 0 100000
Cload6 jack6 0 1e-10
Vsig7 sig7 0 PULSE(-5 5 0 1u 1u 500u 1m)
Eamp7 drive7 0 sig7 fb7 1e5
Risoa7 drive7 mid7 499
Risob7 mid7 jack7 499
Rfb7 jack7 fb7 10k
Cfast7 drive7 fb7 100p
Rload7 jack7 0 100000
Cload7 jack7 0 1e-09
Vsig8 sig8 0 PULSE(-5 5 0 1u 1u 500u 1m)
Eamp8 drive8 0 sig8 fb8 1e5
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
meas tran pset11 FIND v(jack11) AT=400u
meas tran nset11 FIND v(jack11) AT=900u
meas tran pmax12 MAX v(jack12) FROM=0 TO=450u
meas tran nmin12 MIN v(jack12) FROM=500u TO=950u
meas tran pset12 FIND v(jack12) AT=400u
meas tran nset12 FIND v(jack12) AT=900u
quit
.endc
.end
