Takazudo/zudo-osc-hole-field/scripts/pcbgen/fixtures/dense-evidence/fixture-route-dense.kicad_pcb

## KiCad design scripts/pcbgen/fixtures/dense-evidence/fixture-route-dense.kicad_pcb (2026-10-02)

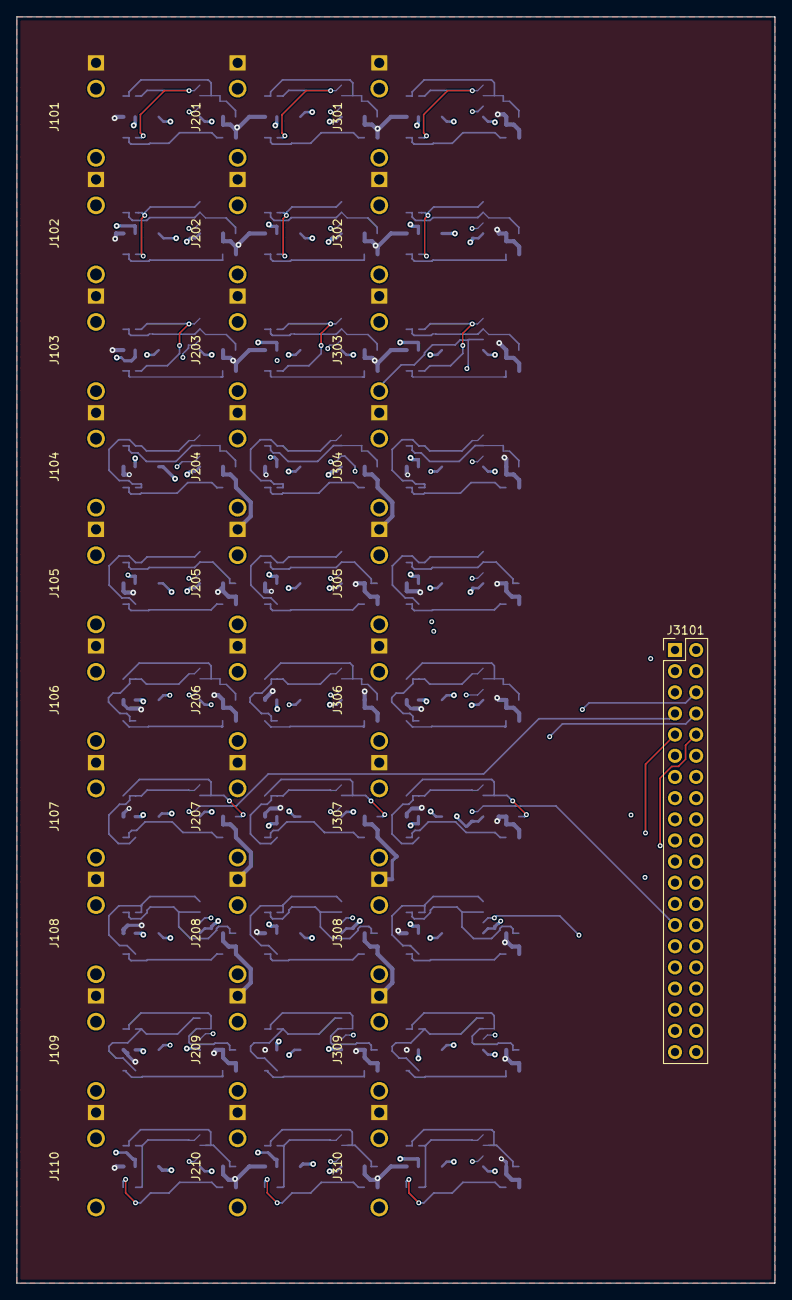
[picture p126: board fixture-route-dense.kicad_pcb from above]

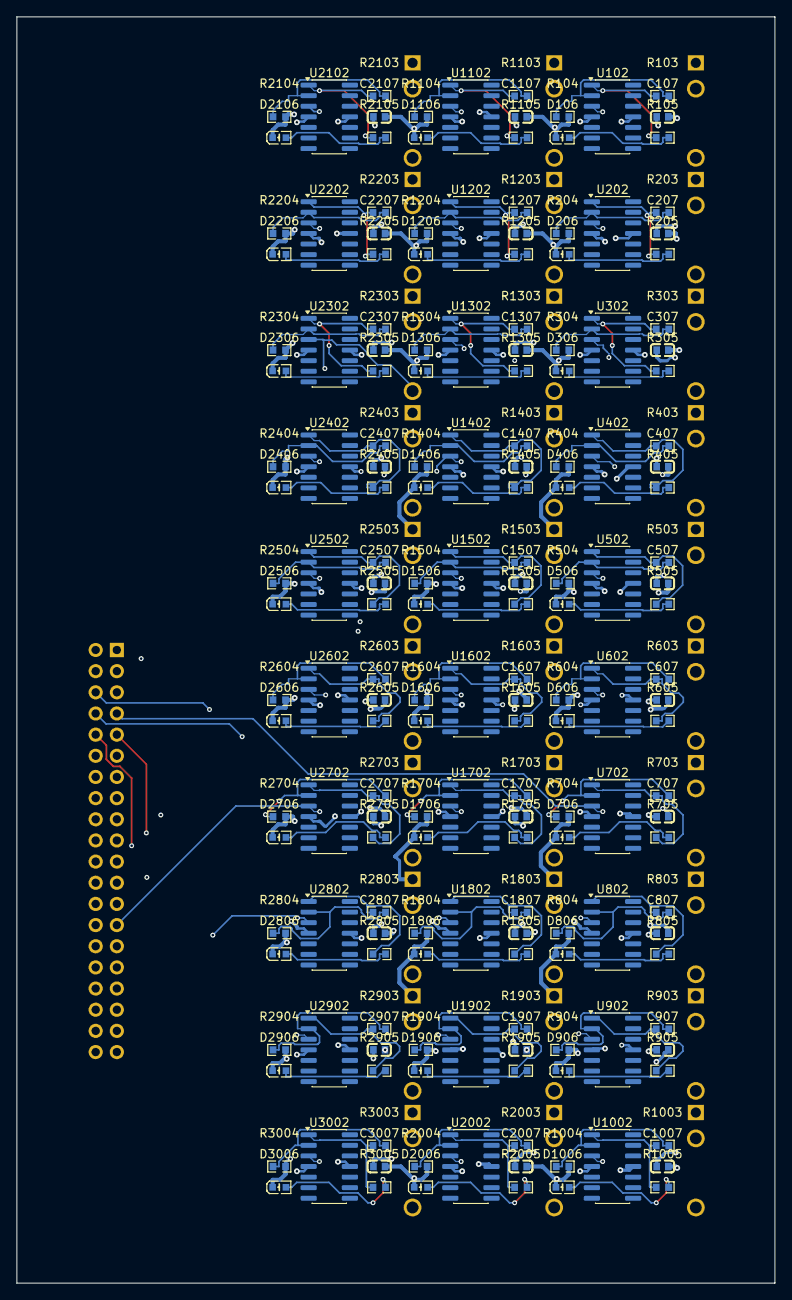
[picture p127: board fixture-route-dense.kicad_pcb from below]

Board: 4 copper layers, 91.0 x 152.0 mm, 211 parts (180 on the bottom side), 123 nets.

Parts:
C107, C207, C307, C407, C507, C607, C707, C807, C907, C1007, C1107, C1207, C1307, C1407, C1507, C1607, C1707, C1807, C1907, C2007, C2107, C2207, C2307, C2407, C2507, C2607, C2707, C2807, C2907, C3007: GRM188R71H104KA93D; C0603
D106, D206, D306, D406, D506, D606, D706, D806, D906, D1006, D1106, D1206, D1306, D1406, D1506, D1606, D1706, D1806, D1906, D2006, D2106, D2206, D2306, D2406, D2506, D2606, D2706, D2806, D2906, D3006: 0603Whitelight_C2290; LED0603-R-RD_WHITE
J101, J102, J103, J104, J105, J106, J107, J108, J109, J110, J201, J202, J203, J204, J205, J206, J207, J208, J209, J210, J301, J302, J303, J304, J305, J306, J307, J308, J309, J310: WQP518MA; Jack_3.5mm_QingPu_WQP518MA
J3101: Conn_02x20_Odd_Even; PinHeader_2x20_P2.54mm_Vertical
R103, R104, R105, R203, R204, R205, R303, R304, R305, R403, R404, R405, R503, R504, R505, R603, R604, R605, R703, R704, R705, R803, R804, R805, R903, R904, R905, R1003, R1004, R1005, R1103, R1104, R1105, R1203, R1204, R1205, R1303, R1304, R1305, R1403, R1404, R1405, R1503, R1504, R1505, R1603, R1604, R1605, R1703, R1704, R1705, R1803, R1804, R1805, R1903, R1904, R1905, R2003, R2004, R2005, R2103, R2104, R2105, R2203, R2204, R2205, R2303, R2304, R2305, R2403, R2404, R2405, R2503, R2504, R2505, R2603, R2604, R2605, R2703, R2704, R2705, R2803, R2804, R2805, R2903, R2904, R2905, R3003, R3004, R3005: RC0603FR-07100KL; R0603
U102, U202, U302, U402, U502, U602, U702, U802, U902, U1002, U1102, U1202, U1302, U1402, U1502, U1602, U1702, U1802, U1902, U2002, U2102, U2202, U2302, U2402, U2502, U2602, U2702, U2802, U2902, U3002: OPA4196IDR; SOIC-14_3.9x8.7mm_P1.27mm

Connections:
+12V: C107.1, C207.1, C307.1, C407.1, C507.1, C607.1, C707.1, C807.1, C907.1, C1007.1, C1107.1, C1207.1, C1307.1, C1407.1, C1507.1, C1607.1, C1707.1, C1807.1, C1907.1, C2007.1, C2107.1, C2207.1, C2307.1, C2407.1, C2507.1, C2607.1, C2707.1, C2807.1, C2907.1, C3007.1, U102.4, U202.4, U302.4, U402.4, U502.4, U602.4, U702.4, U802.4, U902.4, U1002.4, U1102.4, U1202.4, U1302.4, U1402.4, U1502.4, U1602.4, U1702.4, U1802.4, U1902.4, U2002.4, U2102.4, U2202.4, U2302.4, U2402.4, U2502.4, U2602.4, U2702.4, U2802.4, U2902.4, U3002.4
-12V: U102.11, U202.11, U302.11, U402.11, U502.11, U602.11, U702.11, U802.11, U902.11, U1002.11, U1102.11, U1202.11, U1302.11, U1402.11, U1502.11, U1602.11, U1702.11, U1802.11, U1902.11, U2002.11, U2102.11, U2202.11, U2302.11, U2402.11, U2502.11, U2602.11, U2702.11, U2802.11, U2902.11, U3002.11
/C1/DRIVE: R103.1, R105.1, U102.1
/C1/FB: R103.2, R104.1, U102.2
/C1/LED_A: D106.1, R105.2
/C2/DRIVE: R203.1, R205.1, U202.1
/C2/FB: R203.2, R204.1, U202.2
/C2/LED_A: D206.1, R205.2
/C3/DRIVE: R303.1, R305.1, U302.1
/C3/FB: R303.2, R304.1, U302.2
/C3/LED_A: D306.1, R305.2
/C4/DRIVE: R403.1, R405.1, U402.1
/C4/FB: R403.2, R404.1, U402.2
/C4/LED_A: D406.1, R405.2
/C5/DRIVE: R503.1, R505.1, U502.1
/C5/FB: R503.2, R504.1, U502.2
/C5/LED_A: D506.1, R505.2
/C6/DRIVE: R603.1, R605.1, U602.1
/C6/FB: R603.2, R604.1, U602.2
/C6/LED_A: D606.1, R605.2
/C7/DRIVE: R703.1, R705.1, U702.1
/C7/FB: R703.2, R704.1, U702.2
/C7/LED_A: D706.1, R705.2
/C8/DRIVE: R803.1, R805.1, U802.1
/C8/FB: R803.2, R804.1, U802.2
/C8/LED_A: D806.1, R805.2
/C9/DRIVE: R903.1, R905.1, U902.1
/C9/FB: R903.2, R904.1, U902.2
/C9/LED_A: D906.1, R905.2
/C10/DRIVE: R1003.1, R1005.1, U1002.1
/C10/FB: R1003.2, R1004.1, U1002.2
/C10/LED_A: D1006.1, R1005.2
/C11/DRIVE: R1103.1, R1105.1, U1102.1
/C11/FB: R1103.2, R1104.1, U1102.2
/C11/LED_A: D1106.1, R1105.2
/C12/DRIVE: R1203.1, R1205.1, U1202.1
/C12/FB: R1203.2, R1204.1, U1202.2
/C12/LED_A: D1206.1, R1205.2
/C13/DRIVE: R1303.1, R1305.1, U1302.1
/C13/FB: R1303.2, R1304.1, U1302.2
/C13/LED_A: D1306.1, R1305.2
/C14/DRIVE: R1403.1, R1405.1, U1402.1
/C14/FB: R1403.2, R1404.1, U1402.2
/C14/LED_A: D1406.1, R1405.2
/C15/DRIVE: R1503.1, R1505.1, U1502.1
/C15/FB: R1503.2, R1504.1, U1502.2
/C15/LED_A: D1506.1, R1505.2
/C16/DRIVE: R1603.1, R1605.1, U1602.1
/C16/FB: R1603.2, R1604.1, U1602.2
/C16/LED_A: D1606.1, R1605.2
/C17/DRIVE: R1703.1, R1705.1, U1702.1
/C17/FB: R1703.2, R1704.1, U1702.2
/C17/LED_A: D1706.1, R1705.2
/C18/DRIVE: R1803.1, R1805.1, U1802.1
/C18/FB: R1803.2, R1804.1, U1802.2
/C18/LED_A: D1806.1, R1805.2
/C19/DRIVE: R1903.1, R1905.1, U1902.1
/C19/FB: R1903.2, R1904.1, U1902.2
/C19/LED_A: D1906.1, R1905.2
/C20/DRIVE: R2003.1, R2005.1, U2002.1
/C20/FB: R2003.2, R2004.1, U2002.2
/C20/LED_A: D2006.1, R2005.2
/C21/DRIVE: R2103.1, R2105.1, U2102.1
/C21/FB: R2103.2, R2104.1, U2102.2
/C21/LED_A: D2106.1, R2105.2
/C22/DRIVE: R2203.1, R2205.1, U2202.1
/C22/FB: R2203.2, R2204.1, U2202.2
/C22/LED_A: D2206.1, R2205.2
/C23/DRIVE: R2303.1, R2305.1, U2302.1
/C23/FB: R2303.2, R2304.1, U2302.2
/C23/LED_A: D2306.1, R2305.2
/C24/DRIVE: R2403.1, R2405.1, U2402.1
/C24/FB: R2403.2, R2404.1, U2402.2
/C24/LED_A: D2406.1, R2405.2
/C25/DRIVE: R2503.1, R2505.1, U2502.1
/C25/FB: R2503.2, R2504.1, U2502.2
/C25/LED_A: D2506.1, R2505.2
/C26/DRIVE: R2603.1, R2605.1, U2602.1
/C26/FB: R2603.2, R2604.1, U2602.2
/C26/LED_A: D2606.1, R2605.2
/C27/DRIVE: R2703.1, R2705.1, U2702.1
/C27/FB: R2703.2, R2704.1, U2702.2
/C27/LED_A: D2706.1, R2705.2
/C28/DRIVE: R2803.1, R2805.1, U2802.1
/C28/FB: R2803.2, R2804.1, U2802.2
/C28/LED_A: D2806.1, R2805.2
/C29/DRIVE: R2903.1, R2905.1, U2902.1
/C29/FB: R2903.2, R2904.1, U2902.2
/C29/LED_A: D2906.1, R2905.2
/C30/DRIVE: R3003.1, R3005.1, U3002.1
/C30/FB: R3003.2, R3004.1, U3002.2
/C30/LED_A: D3006.1, R3005.2
GND: C107.2, C207.2, C307.2, C407.2, C507.2, C607.2, C707.2, C807.2, C907.2, C1007.2, C1107.2, C1207.2, C1307.2, C1407.2, C1507.2, C1607.2, C1707.2, C1807.2, C1907.2, C2007.2, C2107.2, C2207.2, C2307.2, C2407.2, C2507.2, C2607.2, C2707.2, C2807.2, C2907.2, C3007.2, D106.2, D206.2, D306.2, D406.2, D506.2, D606.2, D706.2, D806.2, D906.2, D1006.2, D1106.2, D1206.2, D1306.2, D1406.2, D1506.2, D1606.2, D1706.2, D1806.2, D1906.2, D2006.2, D2106.2, D2206.2, D2306.2, D2406.2, D2506.2, D2606.2, D2706.2, D2806.2, D2906.2, D3006.2, J101.S, J102.S, J103.S, J104.S, J105.S, J106.S, J107.S, J108.S, J109.S, J110.S, J201.S, J202.S, J203.S, J204.S, J205.S, J206.S, J207.S, J208.S, J209.S, J210.S, J301.S, J302.S, J303.S, J304.S, J305.S, J306.S, J307.S, J308.S, J309.S, J310.S, R104.2, R204.2, R304.2, R404.2, R504.2, R604.2, R704.2, R804.2, R904.2, R1004.2, R1104.2, R1204.2, R1304.2, R1404.2, R1504.2, R1604.2, R1704.2, R1804.2, R1904.2, R2004.2, R2104.2, R2204.2, R2304.2, R2404.2, R2504.2, R2604.2, R2704.2, R2804.2, R2904.2, R3004.2
INPUT_1: J101.T, J3101.1, U102.3
INPUT_2: J102.T, J3101.2, U202.3
INPUT_3: J103.T, J3101.3, U302.3
INPUT_4: J104.T, J3101.4, U402.3
INPUT_5: J105.T, J3101.5, U502.3
INPUT_6: J106.T, J3101.6, U602.3
INPUT_7: J107.T, J3101.7, U702.3
INPUT_8: J108.T, J3101.8, U802.3
INPUT_9: J109.T, J3101.9, U902.3
INPUT_10: J110.T, J3101.10, U1002.3
INPUT_11: J201.T, J3101.11, U1102.3
INPUT_12: J202.T, J3101.12, U1202.3
INPUT_13: J203.T, J3101.13, U1302.3
INPUT_14: J204.T, J3101.14, U1402.3
INPUT_15: J205.T, J3101.15, U1502.3
INPUT_16: J206.T, J3101.16, U1602.3
INPUT_17: J207.T, J3101.17, U1702.3
INPUT_18: J208.T, J3101.18, U1802.3
INPUT_19: J209.T, J3101.19, U1902.3
INPUT_20: J210.T, J3101.20, U2002.3
INPUT_21: J301.T, J3101.21, U2102.3
INPUT_22: J302.T, J3101.22, U2202.3
INPUT_23: J303.T, J3101.23, U2302.3
INPUT_24: J304.T, J3101.24, U2402.3
INPUT_25: J305.T, J3101.25, U2502.3
INPUT_26: J306.T, J3101.26, U2602.3
INPUT_27: J307.T, J3101.27, U2702.3
INPUT_28: J308.T, J3101.28, U2802.3
INPUT_29: J309.T, J3101.29, U2902.3
INPUT_30: J310.T, J3101.30, U3002.3
