Takazudo/zudo-osc-hole-field/schematic/sheets/01_power_interfaces.kicad_sch

## KiCad design schematic/sheets/01_power_interfaces.kicad_sch (2026-09-30)

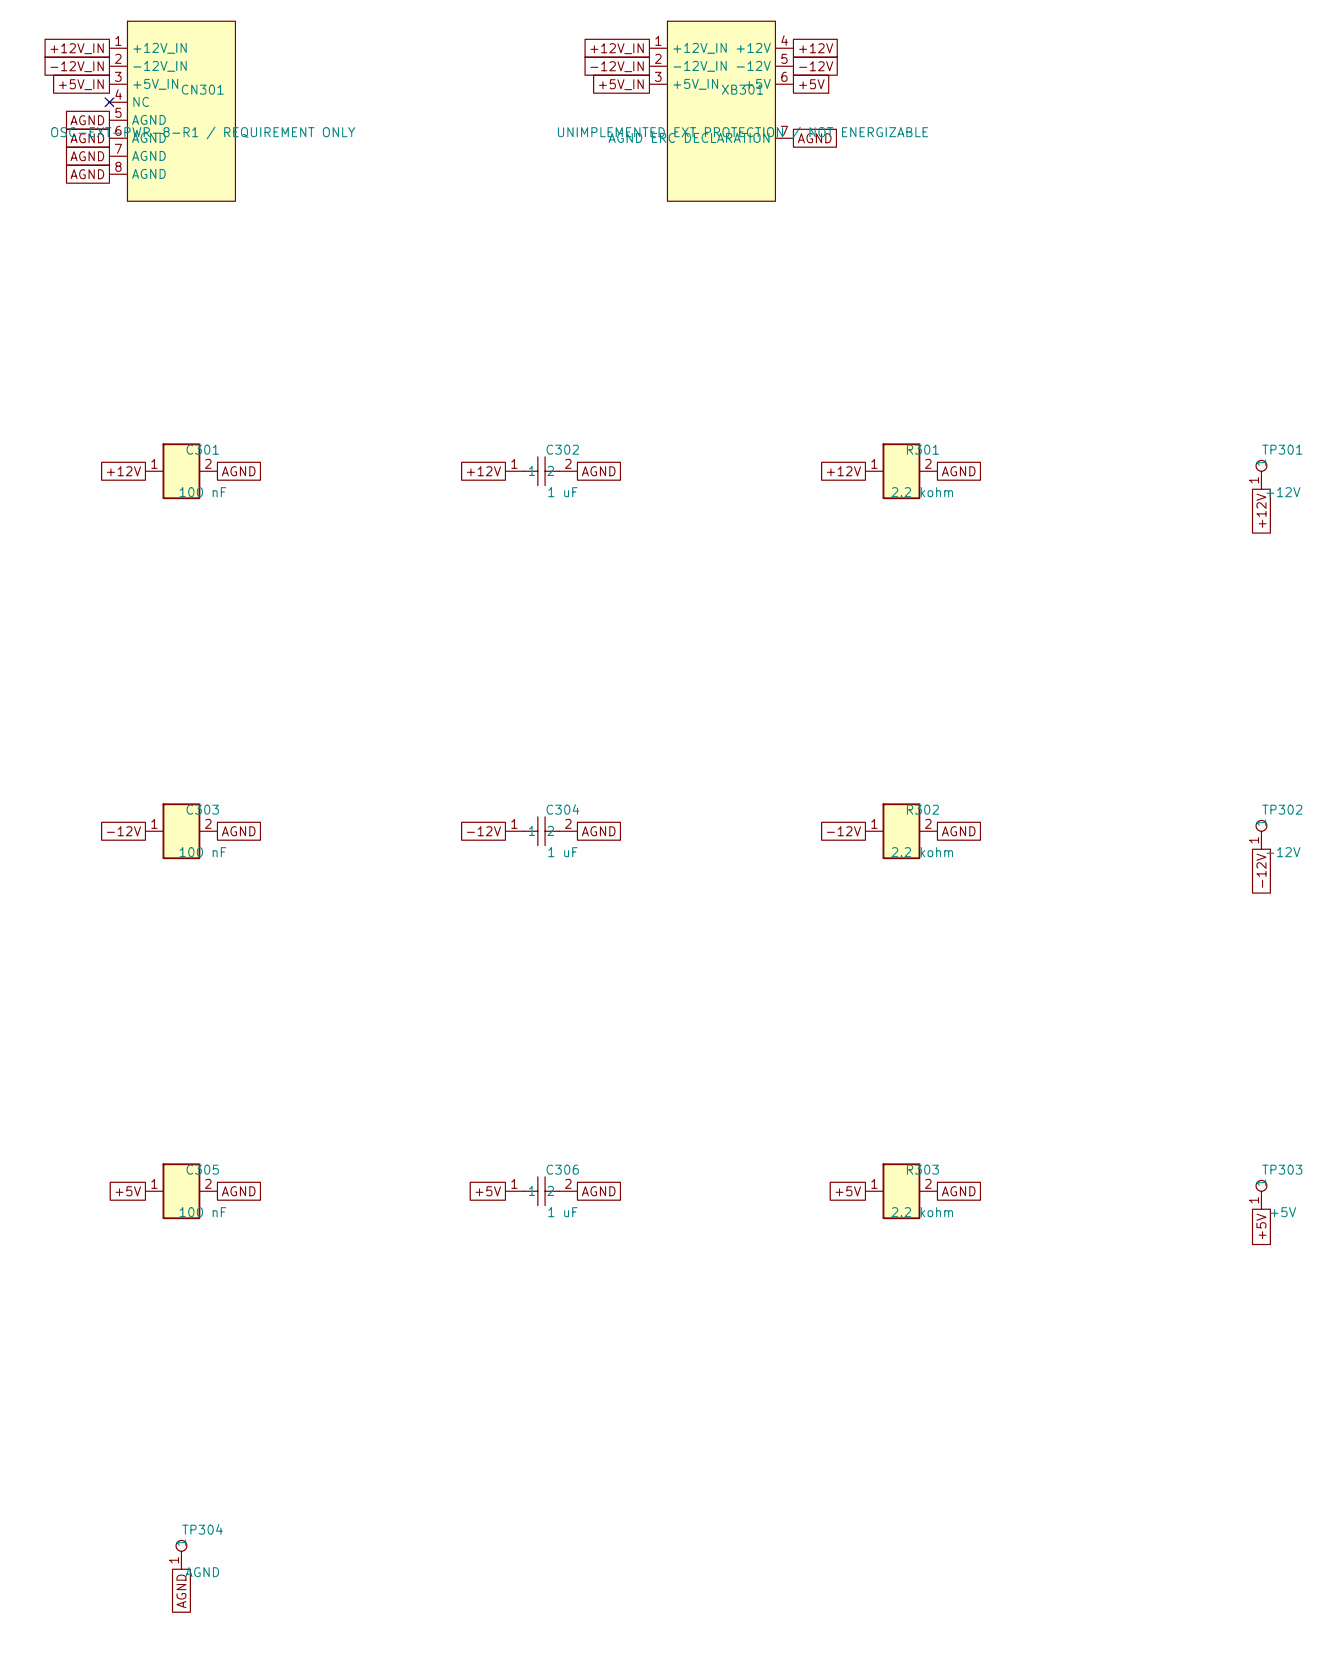
[picture p128: schematic 01_power_interfaces.kicad_sch]

Parts:
C301, C303, C305: 100 nF; C0603; MPN GRM188R71H104KA93D
C302, C304, C306: 1 uF; C0603; MPN CL10A105KB8NNNC; LCSC C15849
CN301: OSC-EXT-PWR-8-R1 / REQUIREMENT ONLY
R301, R302, R303: 2.2 kohm; R0603; MPN RC0603FR-072K2L; LCSC C114662
TP301: +12V; TestPad_D1.5mm; MPN TEST_PAD_D1.5MM
TP302: -12V; TestPad_D1.5mm; MPN TEST_PAD_D1.5MM
TP303: +5V; TestPad_D1.5mm; MPN TEST_PAD_D1.5MM
TP304: AGND; TestPad_D1.5mm; MPN TEST_PAD_D1.5MM
XB301: UNIMPLEMENTED EXT PROTECTION / NOT ENERGIZABLE

Connections:
+5V: C305.1, C306.1, R303.1, TP303.1, XB301.6 (+5V)
+5V_IN: CN301.3 (+5V_IN), XB301.3 (+5V_IN)
+12V: C301.1, C302.1, R301.1, TP301.1, XB301.4 (+12V)
+12V_IN: CN301.1 (+12V_IN), XB301.1 (+12V_IN)
-12V: C303.1, C304.1, R302.1, TP302.1, XB301.5 (-12V)
-12V_IN: CN301.2 (-12V_IN), XB301.2 (-12V_IN)
AGND: C301.2, C302.2, C303.2, C304.2, C305.2, C306.2, CN301.5 (AGND), CN301.6 (AGND), CN301.7 (AGND), CN301.8 (AGND), R301.2, R302.2, R303.2, TP304.1, XB301.7 (AGND ERC DECLARATION)
