Takazudo/zudo-osc-hole-field/schematic/sheets/envelope.kicad_sch

## KiCad design schematic/sheets/envelope.kicad_sch (2026-09-30)

Schematic: envelope.kicad_sch

Parts:
C4101, C4104, C4105, C4106, C4107: 1e-07 F; C0603; MPN GRM188R71H104KA93D
C4102: 1e-06 F; C0603
C4103, C4108: 1 µF; C0603
C4109: 1 nF C0G; C0603
C4110, C4113: 100 nF C0G; C1206; MPN 1206CG104J500NT; LCSC C46348
C4111, C4112: 1e-08 F; C0603
C4114, C4115, C4116, C4117, C4118, C4119, C4120, C4121, C4122, C4123, C4124, C4125, C4126, C4127, C4128, C4129, C4130, C4131, C4132, C4133, C4134, C4135, C4136, C4137, C4138, C4139, C4140, C4141, C4142, C4143, C4144, C4145, C4146, C4147, C4148, C4149, C4150, C4151, C4152, C4153, C4154, C4155, C4156, C4157, C4158, C4159, C4160, C4161, C4162, C4163, C4164, C4165, C4166, C4167, C4168, C4169, C4170, C4171, C4172, C4173, C4174, C4175, C4176, C4177: 100 nF; C0603; MPN GRM188R71H104KA93D
D1301, D1302, D1303, D11305, D11306: APHHS1005QWF/D; LED0402-Kingbright-White; MPN APHHS1005QWF/D
D4101, D4102, D4103, D4105, D4106: BAT54S,215; SOT-23; MPN BAT54S,215
D4104, D4107, D4108, D4109, D4110, D4112, D4113, D4114, D4115, D4117, D4118, D4119, D4120, D4123, D4125: BAS16GW-QX; SOD-123; MPN BAS16GW-QX
J1301, J1302, J1303, J1304, J1305, J1306, J1307: WQP518MA; Jack_3.5mm_QingPu_WQP518MA; MPN WQP518MA
Q4101, Q4104: BCM847BS,115; SOT-363_SC-70-6; MPN BCM847BS,115
Q4102, Q4103, Q4105, Q4106: MMBT3906,215; SOT-23; MPN MMBT3906,215
Q4107, Q4109: MMBT3904,215; SOT-23; MPN MMBT3904,215
Q4108, Q4110: 2N7002,215; SOT-23; MPN 2N7002,215
R4101, R4102, R4108, R4112, R4116, R4119, R4122, R4124, R4126, R4128, R4130: 10000 Ω; R0603
R4103: 22000 Ω; R0603
R4104, R4117: 100000 Ω; R0603; MPN RT0603BRD07100KL
R4105, R4107, R4109, R4111, R4113, R4115: 100000 Ω; R0603; MPN RC0603FR-07100KL
R4106, R4110, R4114, R4123, R4125, R4127, R4129, R4131, R4149, R4166: 1000 Ω; R0603
R4118: 33200 Ω; R0603
R4120: 390000 Ω; R0603
R4121: 4700 Ω; R0603
R4132, R4136, R4138, R4143, R4145, R4151, R4153, R4154, R4155, R4157, R4168, R4170, R4171, R4172, R4174, R4183, R4184, R4185, R4186, R4187, R4188, R4189, R4190: 100 kΩ; R0603; MPN RT0603BRD07100KL
R4133, R4134: 47 kΩ; R0603
R4135: 60 kΩ; R0603
R4137: 80 kΩ; R0603
R4139: 40 kΩ; R0603
R4140, R4156, R4173: 10 kΩ; R0603
R4141: 79 kΩ; R0603
R4142, R4162, R4163, R4179, R4180: 22 kΩ; R0603
R4144, R4146: 10 MΩ; R0603
R4147, R4148: 4.7 kΩ; R0603
R4150, R4167: 1e+07 Ω; R0603
R4152, R4158, R4169, R4175: 200 kΩ; R0603
R4159, R4176: 3.3 kΩ; R0603
R4160, R4165, R4177, R4182, R4192, R4194: 1 kΩ; R0603
R4161, R4178: 300 kΩ; R0603
R4164, R4181: 470 kΩ; R0603
R4191, R4193: 899 kΩ; R0603
R4195, R4196, R4197, R4198: 100 Ω; R0603
R4199: 64 kΩ; R0603
RB4101: 80 kΩ; R0603
RB4102, RB4103: 100 kΩ; R0603; MPN RT0603BRD07100KL
RB4104: 400 kΩ; R0603
RB4105, RB4106, RB4107, RB4108, RB4109, RB4110, RB4111, RB4112: 499 Ω; R_1210_3225Metric; MPN RC1210FR-07499RL
RB4113, RB4114, RB4115: 5600 Ω; R0603
RB4116, RB4122: 150000 Ω; R0603
RB4117, RB4118, RB4123, RB4124: 10000 Ω; R0603
RB4119, RB4125: 1000 Ω; R0603
RB4120, RB4126: 1200 Ω; R0603
RB4121, RB4127: 100000 Ω; R0603; MPN RC0603FR-07100KL
RV1305, RV1306: PTV09A-4020F-B104; PTV09A-4020F; MPN PTV09A-4020F-B104
RV4102, RV4106: 1 kΩ; Potentiometer_Bourns_TC33X_Vertical; MPN TC33X-2-102E
RV4103, RV4107: 50 kΩ; Potentiometer_Bourns_TC33X_Vertical
RV4104, RV4108: 10 kΩ; Potentiometer_Bourns_TC33X_Vertical; MPN TC33X-2-103E
SW1301: 2MS3T1B1M2QES; Toggle_Dailywell_2MS_T1B1M2; MPN 2MS3T1B1M2QES
SW1302, SW1303: 2MS1T1B1M2QES-5; Toggle_Dailywell_2MS_T1B1M2; MPN 2MS1T1B1M2QES-5; LCSC C908280
SW1304: B3F-1020; Button_Omron_B3F_6x6_P6.5x4.5; MPN B3F-1020; LCSC C722171
U4101: REF5050AIDR; SOIC-8_3.9x4.9mm_P1.27mm; MPN REF5050AIDR; LCSC C27804
U4102, U4103, U4104, U4106, U4108: ADG5412FBRUZ; TSSOP-16_4.4x5mm_P0.65mm; MPN ADG5412FBRUZ; LCSC C579073
U4105: CD74HC221M96; SOIC-16_3.9x9.9mm_P1.27mm; MPN CD74HC221M96; LCSC C133954
U4107: LM13700M/NOPB; SOIC-16_3.9x9.9mm_P1.27mm; MPN LM13700M/NOPB; LCSC C1346265
U4109, U4110: LM393BIDR; SOIC-8_3.9x4.9mm_P1.27mm; MPN LM393BIDR
U4111, U4112: SN74HC14DR; SOIC-14_3.9x8.7mm_P1.27mm; MPN SN74HC14DR
U4113, U4114, U4115, U4116, U4117, U4118, U4119, U4120, U4121, U4122, U4123, U4124, U4125, U4126, U4127, U4128, U4129: SN74HC00DR; SOIC-14_3.9x8.7mm_P1.27mm; MPN SN74HC00DR
U4130, U4131, U4132, U4133, U4134, U4135, U4136, U4137, U4138: SN74HC74DR; SOIC-14_3.9x8.7mm_P1.27mm; MPN SN74HC74DR
U4139, U4140, U4141: OPA4197IPWR; TSSOP-14_4.4x5mm_P0.65mm; MPN OPA4197IPWR; LCSC C2057327
U4142, U4143, U4144, U4145, U4146, U4147, U4148: OPA4196IDR; SOIC-14_3.9x8.7mm_P1.27mm; MPN OPA4196IDR; LCSC C2057385

Connections:
+5V: C4121.1, C4130.1, C4131.1, C4132.1, C4133.1, C4134.1, C4135.1, C4136.1, C4137.1, C4138.1, C4139.1, C4140.1, C4141.1, C4142.1, C4143.1, C4144.1, C4145.1, C4146.1, C4147.1, C4148.1, C4149.1, C4150.1, C4151.1, C4152.1, C4153.1, C4154.1, C4155.1, C4156.1, C4157.1, D4104.1 (K), R4106.1, R4110.1, R4114.1, R4121.1, R4122.1, R4124.1, R4126.1, R4128.1, R4130.1, R4132.1, R4134.1, R4147.1, R4148.1, RB4120.1, RB4121.2, RB4126.1, RB4127.2, U4105.16 (VCC), U4111.14 (VCC), U4112.14 (VCC), U4113.14 (VCC), U4114.14 (VCC), U4115.14 (VCC), U4116.14 (VCC), U4117.14 (VCC), U4118.14 (VCC), U4119.14 (VCC), U4120.14 (VCC), U4121.14 (VCC), U4122.14 (VCC), U4123.14 (VCC), U4124.14 (VCC), U4125.14 (VCC), U4126.14 (VCC), U4127.14 (VCC), U4128.14 (VCC), U4129.14 (VCC), U4130.2 (D), U4130.4 (~S), U4130.10 (~S), U4130.14 (VCC), U4131.4 (~S), U4131.10 (~S), U4131.14 (VCC), U4132.4 (~S), U4132.10 (~S), U4132.14 (VCC), U4133.4 (~S), U4133.10 (~S), U4133.14 (VCC), U4134.4 (~S), U4134.10 (~S), U4134.14 (VCC), U4135.4 (~S), U4135.10 (~S), U4135.14 (VCC), U4136.4 (~S), U4136.10 (~S), U4136.14 (VCC), U4137.4 (~S), U4137.10 (~S), U4137.14 (VCC), U4138.4 (~S), U4138.10 (~S), U4138.14 (VCC)
+12V: C4101.1, C4114.1, C4115.1, C4117.1, C4119.1, C4122.1, C4124.1, C4126.1, C4128.1, C4129.1, C4158.1, C4160.1, C4162.1, C4164.1, C4166.1, C4168.1, C4170.1, C4172.1, C4174.1, C4176.1, D4101.2 (K), D4102.2 (K), D4103.2 (K), Q4102.2 (E), Q4103.2 (E), Q4105.2 (E), Q4106.2 (E), U4101.2 (Vin), U4102.13 (VDD), U4103.13 (VDD), U4104.13 (VDD), U4106.13 (VDD), U4107.11 (V+), U4108.13 (VDD), U4109.8 (V+), U4110.8 (V+), U4139.4 (V+), U4140.4 (V+), U4141.4 (V+), U4142.4 (V+), U4143.4 (V+), U4144.4 (V+), U4145.4 (V+), U4146.4 (V+), U4147.4 (V+), U4148.4 (V+)
-12V: C4116.1, C4118.1, C4120.1, C4123.1, C4125.1, C4127.1, C4159.1, C4161.1, C4163.1, C4165.1, C4167.1, C4169.1, C4171.1, C4173.1, C4175.1, C4177.1, D4101.1 (A), D4102.1 (A), D4103.1 (A), U4102.4 (VSS), U4103.4 (VSS), U4104.4 (VSS), U4106.4 (VSS), U4107.6 (V-), U4108.4 (VSS), U4139.11 (V-), U4140.11 (V-), U4141.11 (V-), U4142.11 (V-), U4143.11 (V-), U4144.11 (V-), U4145.11 (V-), U4146.11 (V-), U4147.11 (V-), U4148.11 (V-)
AGND: C4101.2, C4102.2, C4103.2, C4104.2, C4105.2, C4106.2, C4107.2, C4108.2, C4109.2, C4111.2, C4112.2, C4113.2, C4114.2, C4115.2, C4116.2, C4117.2, C4118.2, C4119.2, C4120.2, C4121.2, C4122.2, C4123.2, C4124.2, C4125.2, C4126.2, C4127.2, C4128.2, C4129.2, C4130.2, C4131.2, C4132.2, C4133.2, C4134.2, C4135.2, C4136.2, C4137.2, C4138.2, C4139.2, C4140.2, C4141.2, C4142.2, C4143.2, C4144.2, C4145.2, C4146.2, C4147.2, C4148.2, C4149.2, C4150.2, C4151.2, C4152.2, C4153.2, C4154.2, C4155.2, C4156.2, C4157.2, C4158.2, C4159.2, C4160.2, C4161.2, C4162.2, C4163.2, C4164.2, C4165.2, C4166.2, C4167.2, C4168.2, C4169.2, C4170.2, C4171.2, C4172.2, C4173.2, C4174.2, C4175.2, C4176.2, C4177.2, D4105.1 (A), D4106.1 (A), J1301.S (Sleeve), J1302.S (Sleeve), J1303.S (Sleeve), J1304.S (Sleeve), J1305.S (Sleeve), J1306.S (Sleeve), J1307.S (Sleeve), Q4101.2 (B1), Q4104.2 (B1), Q4108.2 (S), Q4110.2 (S), R4104.2, R4105.2, R4107.2, R4109.2, R4111.2, R4113.2, R4115.2, R4136.2, R4138.2, R4140.2, R4142.2, R4150.2, R4165.2, R4167.2, R4182.2, R4184.2, R4190.2, R4192.2, R4194.2, RB4101.2, RB4104.2, RB4113.2, RB4114.2, RB4115.2, RB4117.2, RB4119.2, RB4123.2, RB4125.2, RV1305.1 (CCW), RV1306.1 (CCW), SW1301.2 (Common), SW1302.2 (Common), SW1303.2 (Common), SW1304.1 (B), SW1304.2 (B), U4101.4 (GND), U4102.5 (GND), U4102.6 (S4), U4102.7 (D4), U4102.8 (IN4), U4102.9 (IN3), U4102.10 (D3), U4102.11 (S3), U4102.14 (S2), U4102.15 (D2), U4102.16 (IN2), U4103.5 (GND), U4103.6 (S4), U4103.7 (D4), U4103.8 (IN4), U4103.9 (IN3), U4103.10 (D3), U4103.11 (S3), U4103.14 (S2), U4103.15 (D2), U4103.16 (IN2), U4104.5 (GND), U4104.6 (S4), U4104.7 (D4), U4104.8 (IN4), U4104.9 (IN3), U4104.10 (D3), U4104.11 (S3), U4104.14 (S2), U4104.15 (D2), U4104.16 (IN2), U4105.1 (1A), U4105.8 (GND), U4105.9 (2A), U4105.10 (2B), U4105.11 (2R), U4106.5 (GND), U4107.7, U4107.10, U4108.5 (GND), U4108.6 (S4), U4108.7 (D4), U4108.8 (IN4), U4108.9 (IN3), U4108.10 (D3), U4108.11 (S3), U4108.15 (D2), U4109.4 (GND), U4110.4 (GND), U4110.5 (+), U4111.7 (GND), U4111.13, U4112.7 (GND), U4113.7 (GND), U4114.7 (GND), U4115.7 (GND), U4116.7 (GND), U4117.7 (GND), U4118.7 (GND), U4119.7 (GND), U4120.7 (GND), U4121.7 (GND), U4122.7 (GND), U4123.7 (GND), U4124.7 (GND), U4125.7 (GND), U4126.7 (GND), U4127.7 (GND), U4128.7 (GND), U4129.7 (GND), U4129.12, U4129.13, U4130.7 (GND), U4131.7 (GND), U4132.7 (GND), U4133.7 (GND), U4134.7 (GND), U4135.7 (GND), U4136.7 (GND), U4137.7 (GND), U4138.7 (GND), U4138.11 (C), U4138.12 (D), U4138.13 (~R), U4139.5 (+), U4140.10 (+), U4140.12 (+), U4141.3 (+), U4141.5 (+), U4141.12 (+), U4142.10 (+), U4142.12 (+), U4143.5 (+), U4143.10 (+), U4144.5 (+), U4144.10 (+), U4145.12 (+), U4148.10 (+), U4148.12 (+)
ASR: U4116.4, U4118.5, U4120.1, U4132.9 (Q)
ASR_CONTACT: R4124.2, R4125.1, SW1301.1 (Right)
ASR_RAW: U4111.4, U4132.2 (D)
ASR_SYNC: U4132.5 (Q), U4132.12 (D)
BIP_CORE: RB4103.1, U4145.8, U4147.3 (+)
BIP_PLUS: R4199.2, RB4101.1, U4145.10 (+)
BIP_SUM: RB4102.2, RB4103.2, RB4104.1, U4145.9 (-)
BIP_TIP: J1305.T (Tip), RB4108.2
BOTTOM: U4123.2, U4136.5 (Q)
BOTTOM_LOW: R4146.1, R4148.2, U4110.1, U4112.13
BOTTOM_N: U4119.13, U4136.6 (~Q)
BOTTOM_RAW: U4112.12, U4125.2, U4135.12 (D)
BOTTOM_SENSE: R4145.2, R4146.2, U4110.3 (+)
BOTTOM_SYNC: U4135.9 (Q), U4136.2 (D)
C2cda1f_DEBOUNCE: C4107.1, R4131.2, U4111.11
C5dbedd_DRIVE: RB4107.1, U4147.1, U4147.2 (-)
C5dbedd_ISO_MID: RB4107.2, RB4108.1
C7b4897_SENSE: D4103.3 (COM), R4116.2, U4146.10 (+)
C8c002f_DRIVE: D4112.2 (A), D4114.1 (K), U4148.1
C8c002f_LED_A: D1302.2 (A), D4112.1 (K), D4113.1 (K)
C8c002f_LED_K: D1302.1 (K), D4114.2 (A), D4115.2 (A)
C8c002f_SENSE: D4113.2 (A), D4115.1 (K), RB4114.1, U4148.2 (-)
C8c25a4_DEBOUNCE: C4104.1, R4125.2, U4111.3
C8df228_BASE: D4123.1 (K), Q4107.1 (B), RB4118.2
C8df228_BASE_DRIVE: RB4118.1, U4142.1
C8df228_COMMAND: Q4108.3 (D), RB4116.2, RB4117.1, U4142.3 (+)
C8df228_EMITTER: D4123.2 (A), Q4107.2 (E), RB4119.1, U4142.2 (-)
C8df228_LED_A: D11305.2 (A), RB4120.2
C8df228_LED_K: D11305.1 (K), Q4107.3 (C)
C9f1934_DRIVE: D4117.2 (A), D4119.1 (K), U4148.7
C9f1934_LED_A: D1303.2 (A), D4117.1 (K), D4118.1 (K)
C9f1934_LED_K: D1303.1 (K), D4119.2 (A), D4120.2 (A)
C9f1934_SENSE: D4118.2 (A), D4120.1 (K), RB4115.1, U4148.6 (-)
C33e306_SENSE: D4101.3 (COM), R4108.2, U4146.3 (+)
C76e00a_DEBOUNCE: C4106.1, R4129.2, U4111.9
C887c55_ENABLE: R4109.1, R4110.2, U4103.1 (IN1)
C2882f4_SENSE: D4102.3 (COM), R4112.2, U4146.5 (+)
C992951_DEBOUNCE: C4105.1, R4127.2, U4111.5
CLOCK: R4133.1, U4112.8, U4130.3 (C), U4130.11 (C), U4131.3 (C), U4131.11 (C), U4132.3 (C), U4132.11 (C), U4133.3 (C), U4133.11 (C), U4134.3 (C), U4134.11 (C), U4135.3 (C), U4135.11 (C), U4136.3 (C), U4136.11 (C), U4137.3 (C), U4137.11 (C), U4138.3 (C)
CLOCK_RC: C4109.1, R4133.2, U4112.9
COMPLETE: U4105.2 (1B), U4138.5 (Q)
CORE_PACK_OPA4196IDR_0_IO_UNUSED3: U4142.8, U4142.9 (-)
CORE_PACK_OPA4196IDR_0_IO_UNUSED4: U4142.13 (-), U4142.14
CORE_PACK_OPA4196IDR_3_IO_UNUSED4: U4145.13 (-), U4145.14
CORE_PACK_OPA4197IPWR_2_IO_UNUSED4: U4141.13 (-), U4141.14
CURVED: U4111.8, U4126.9, U4126.10, U4127.13, U4128.13
CURVED_CONTACT: R4128.2, R4129.1, SW1302.3 (Left)
Ca18182_CMP_OUT: R4120.1, R4121.2, U4109.1, U4112.1
Ca18182_GATE_SENSE: R4117.2, R4118.2, U4109.2 (-)
Ca18182_THRESH: R4119.2, R4120.2, U4109.3 (+)
Cae74f8_DRIVE: D4107.2 (A), D4109.1 (K), U4147.14
Cae74f8_LED_A: D1301.2 (A), D4107.1 (K), D4108.1 (K)
Cae74f8_LED_K: D1301.1 (K), D4109.2 (A), D4110.2 (A)
Cae74f8_SENSE: D4108.2 (A), D4110.1 (K), RB4113.1, U4147.13 (-)
Caf802b_DRIVE: RB4109.1, U4147.6 (-), U4147.7
Caf802b_ISO_MID: RB4109.2, RB4110.1
Cb1f6a5_BASE: D4125.1 (K), Q4109.1 (B), RB4124.2
Cb1f6a5_BASE_DRIVE: RB4124.1, U4142.7
Cb1f6a5_COMMAND: Q4110.3 (D), RB4122.2, RB4123.1, U4142.5 (+)
Cb1f6a5_EMITTER: D4125.2 (A), Q4109.2 (E), RB4125.1, U4142.6 (-)
Cb1f6a5_LED_A: D11306.2 (A), RB4126.2
Cb1f6a5_LED_K: D11306.1 (K), Q4109.3 (C)
Cb80f06_W: R4149.1, RV1305.2 (WIPER)
Cb80f06_W_SENSE: C4111.1, R4149.2, R4150.1, U4143.3 (+)
Cb2412d_DEBOUNCE: C4103.1, R4123.2, U4111.1
Cc9f2ea_DRIVE: RB4105.1, U4146.13 (-), U4146.14
Cc9f2ea_ISO_MID: RB4105.2, RB4106.1
Cd69090_W: R4166.1, RV1306.2 (WIPER)
Cd69090_W_SENSE: C4112.1, R4166.2, R4167.1, U4144.3 (+)
Ce697df_ENABLE: R4113.1, R4114.2, U4104.1 (IN1)
Ce82060_DRIVE: RB4111.1, U4147.8, U4147.9 (-)
Ce82060_ISO_MID: RB4111.2, RB4112.1
Cf89b5a_GATE_RAW: R4103.2, R4104.1, U4139.10 (+)
Cf89b5a_INV: R4101.2, R4102.2, U4139.6 (-)
Cf89b5a_RAW_5V: C4102.1, U4101.6 (Vout), U4139.3 (+)
Cf758e9_ENABLE: R4105.1, R4106.2, U4102.1 (IN1)
D_COMPLETE: U4123.11, U4138.2 (D)
D_FALL: U4122.6, U4137.12 (D)
D_HOLD: U4119.8, U4137.2 (D)
D_RISE: U4117.8, U4136.12 (D)
ENV_BUFFER: R4185.1, R4187.1, R4199.1, RB4116.1, RB4122.1, U4141.8, U4141.9 (-), U4146.12 (+)
ENV_STORAGE: C4113.1, R4195.2, R4196.2, R4197.2, R4198.2, U4141.10 (+)
ENV_TIP: J1304.T (Tip), RB4106.2
EOC: U4105.4 (1Q), U4115.1, U4115.2, U4147.5 (+)
EOC_C: C4110.2, U4105.14 (1CX)
EOC_RCX: C4110.1, R4134.2, U4105.15 (1RXCX)
EOC_TIP: J1306.T (Tip), RB4110.2
FALL: U4119.12, U4122.10, U4124.2, U4125.1, U4129.9, U4129.10, U4137.9 (Q)
FALL_BIAS_SOURCE: Q4106.3 (C), R4180.1
FALL_BUFFER: R4169.1, U4146.8, U4146.9 (-), U4148.5 (+)
FALL_CURVE: U4106.8 (IN4), U4129.3
FALL_CURVE_FB: R4189.2, R4190.1, U4145.6 (-)
FALL_CURVE_PLUS: R4187.2, R4188.2, U4145.5 (+)
FALL_CURVE_V: R4145.1, R4189.1, U4106.7 (D4), U4109.6 (-), U4145.7
FALL_DRIVE: R4193.1, U4106.6 (S4), U4106.11 (S3)
FALL_EXPO_BASE: Q4104.5 (B2), R4177.2
FALL_EXPO_COLLECTOR: Q4104.3 (C2), R4179.2
FALL_EXPO_DRIVE: R4176.1, R4177.1, U4141.1
FALL_EXPO_EMITTER: Q4104.1 (E1), Q4104.4 (E2), U4141.7
FALL_EXPO_REF: Q4104.6 (C1), RV4107.2 (Wiper), RV4107.3 (CW), U4141.6 (-)
FALL_EXPO_SUM: R4174.2, R4175.2, RV4106.2 (Wiper), RV4106.3 (CW), U4141.2 (-)
FALL_IABC: R4180.2, U4107.16
FALL_LINEAR: U4106.9 (IN3), U4128.8
FALL_MANUAL: R4168.1, U4144.1, U4144.2 (-)
FALL_MIRROR_BASE: Q4105.1 (B), Q4105.3 (C), Q4106.1 (B), R4179.1
FALL_N: U4114.5, U4137.8 (~Q)
FALL_OFFSET: R4181.2, R4182.1, U4107.14 (+)
FALL_OFFSET_TRIM: R4181.1, RV4108.2 (Wiper)
FALL_OTA_CURRENT: R4196.1, U4107.12
FALL_OTA_SIGNAL: R4193.2, R4194.1, U4107.13 (-)
FALL_PROTECTED: R4115.1, R4116.1, U4104.2 (D1)
FALL_REF_TRIM: R4178.2, RV4107.1 (CCW)
FALL_SCALE_TRIM: R4176.2, RV4106.1 (CCW)
FALL_TIME: R4174.1, U4144.13 (-), U4144.14
FALL_TIME_CLAMP: D4106.3 (COM), R4173.2, U4144.12 (+)
FALL_TIME_INV: R4171.2, R4172.2, U4144.9 (-)
FALL_TIME_NEG: R4170.1, R4171.1, U4144.7
FALL_TIME_RAW: R4172.1, R4173.1, U4144.8
FALL_TIME_SUM: R4168.2, R4169.2, R4170.2, U4144.6 (-)
FALL_TIP: J1303.T (Tip), U4104.3 (S1)
FLOOR_REF: R4141.2, R4142.1, U4110.2 (-)
GATE: U4114.12, U4118.13, U4120.2, U4131.9 (Q), U4134.2 (D)
GATE_N: U4116.5, U4131.8 (~Q)
GATE_PREV_N: U4114.13, U4134.6 (~Q)
GATE_RAW: U4113.8, U4131.2 (D)
GATE_REF: R4119.1, U4139.8, U4139.9 (-)
GATE_SYNC: U4131.5 (Q), U4131.12 (D)
HOLD: U4121.1, U4137.5 (Q)
HOLD_CLAMP: R4197.1, U4108.2 (D1)
HOLD_ENABLE: U4108.1 (IN1), U4126.6
HOLD_N: U4113.13, U4118.1, U4126.4, U4137.6 (~Q)
IDLE: U4114.8, U4115.5
IDLE_CLAMP: R4198.1, U4108.14 (S2)
L001: U4113.3, U4113.9
L002: U4113.6, U4113.10
L004: U4113.11, U4114.1, U4114.2
L005: U4114.3, U4114.4
L006: U4114.6, U4114.9, U4114.10, U4125.5
L008: U4114.11, U4116.1
L010: U4115.3, U4115.13
L011: U4115.6, U4115.9, U4115.10
L012: U4115.8, U4115.12
L013: U4115.11, U4116.2
L016: U4116.6, U4117.2, U4120.10
L017: U4116.8, U4116.12, U4116.13
L018: U4116.11, U4117.1
L019: U4117.3, U4117.10
L021: U4117.6, U4117.9, U4118.4, U4122.1, U4123.10
L023: U4117.11, U4118.2
L025: U4118.3, U4119.5
L026: U4118.6, U4118.9, U4118.10
L027: U4118.8, U4118.12
L028: U4118.11, U4119.1, U4119.2
L029: U4119.3, U4119.4
L030: U4119.6, U4119.9, U4119.10
L032: U4119.11, U4121.4
L034: U4120.3, U4120.5, U4121.2
L036: U4120.6, U4120.9
L039: U4120.8, U4120.13
L040: U4120.11, U4121.5
L042: U4121.3, U4121.13
L044: U4121.6, U4121.9, U4121.10
L045: U4121.8, U4121.12
L046: U4121.11, U4122.2
L047: U4122.3, U4122.4, U4122.5
L049: U4122.8, U4122.12, U4122.13
L050: U4122.11, U4123.1, U4128.4, U4128.12
L051: U4123.3, U4123.4, U4123.5
L052: U4123.6, U4123.9
L053: U4123.8, U4123.12, U4123.13
L055: U4124.3, U4124.12
L057: U4124.6, U4124.9
L058: U4124.8, U4124.13
L061: U4125.3, U4125.13
L063: U4125.6, U4125.9, U4125.10
L064: U4125.8, U4125.12
L066: U4126.3, U4126.5
L069: U4126.8, U4127.5, U4128.5
L070: U4126.11, U4127.1, U4127.2
L071: U4127.3, U4127.4, U4127.12
L072: U4127.6, U4127.9, U4127.10
L074: U4127.11, U4128.1, U4128.2
L076: U4128.6, U4128.9, U4128.10
L078: U4128.11, U4129.1, U4129.2
LED_PACK_OPA4196IDR_1_IO_UNUSED3: U4148.8, U4148.9 (-)
LED_PACK_OPA4196IDR_1_IO_UNUSED4: U4148.13 (-), U4148.14
LOOP: U4115.4, U4133.9 (Q)
LOOP_CONTACT: R4126.2, R4127.1, SW1301.3 (Left)
LOOP_RAW: U4111.6, U4133.2 (D)
LOOP_SYNC: U4133.5 (Q), U4133.12 (D)
NOT_FALL: Q4110.1 (G), RB4127.1, U4129.8
NOT_RISE: Q4108.1 (G), RB4121.1, U4129.6
POR_LOW: U4112.4, U4112.5
POR_RC: C4108.1, D4104.2 (A), R4132.2, U4112.3
READY: U4105.3 (1R), U4122.9, U4125.4, U4126.12, U4130.9 (Q), U4131.1 (~R), U4131.13 (~R), U4132.1 (~R), U4132.13 (~R), U4133.1 (~R), U4133.13 (~R), U4134.1 (~R), U4134.13 (~R), U4135.1 (~R), U4135.13 (~R), U4136.1 (~R), U4136.13 (~R), U4137.1 (~R), U4137.13 (~R), U4138.1 (~R)
READY1: U4130.5 (Q), U4130.12 (D)
REF1: R4188.1, U4140.6 (-), U4140.7
REF1_RAW: R4139.2, R4140.1, U4140.5 (+)
REF5: D4105.2 (K), D4106.2 (K), R4101.1, R4103.1, R4118.1, R4139.1, R4141.1, R4161.1, R4178.1, RB4102.1, RV1305.3 (CW), RV1306.3 (CW), RV4104.3 (CW), RV4108.3 (CW), U4110.6 (-), U4139.1, U4139.2 (-), U4139.12 (+), U4140.3 (+)
REF8: R4135.1, U4108.3 (S1), U4139.14
REF8_FB: R4135.2, R4136.1, U4139.13 (-)
REF9: R4137.1, R4143.1, R4183.1, U4106.3 (S1), U4106.10 (D3), U4140.1
REF9_FB: R4137.2, R4138.1, U4140.2 (-)
REF45: R4183.2, R4184.1, U4145.3 (+)
REFN5: R4102.1, R4158.1, R4175.1, RV4104.1 (CCW), RV4108.1 (CCW), U4139.7
RESET_CAP: U4108.16 (IN2), U4125.11
RESET_N: U4112.6, U4130.1 (~R), U4130.13 (~R)
RISE: U4116.9, U4117.12, U4120.12, U4124.10, U4126.1, U4126.13, U4129.4, U4129.5, U4136.9 (Q)
RISE_BIAS_SOURCE: Q4103.3 (C), R4163.1
RISE_BUFFER: R4152.1, U4146.6 (-), U4146.7, U4148.3 (+)
RISE_CURVE: U4106.16 (IN2), U4128.3
RISE_CURVE_SUM: R4185.2, R4186.2, U4145.2 (-)
RISE_CURVE_V: R4186.1, U4106.15 (D2), U4145.1
RISE_DRIVE: R4191.1, U4106.2 (D1), U4106.14 (S2)
RISE_EXPO_BASE: Q4101.5 (B2), R4160.2
RISE_EXPO_COLLECTOR: Q4101.3 (C2), R4162.2
RISE_EXPO_DRIVE: R4159.1, R4160.1, U4140.8
RISE_EXPO_EMITTER: Q4101.1 (E1), Q4101.4 (E2), U4140.14
RISE_EXPO_REF: Q4101.6 (C1), RV4103.2 (Wiper), RV4103.3 (CW), U4140.13 (-)
RISE_EXPO_SUM: R4157.2, R4158.2, RV4102.2 (Wiper), RV4102.3 (CW), U4140.9 (-)
RISE_IABC: R4163.2, U4107.1
RISE_LINEAR: U4106.1 (IN1), U4127.8
RISE_MANUAL: R4151.1, U4143.1, U4143.2 (-)
RISE_MIRROR_BASE: Q4102.1 (B), Q4102.3 (C), Q4103.1 (B), R4162.1
RISE_N: U4113.12, U4136.8 (~Q)
RISE_OFFSET: R4164.2, R4165.1, U4107.4 (-)
RISE_OFFSET_TRIM: R4164.1, RV4104.2 (Wiper)
RISE_OTA_CURRENT: R4195.1, U4107.5
RISE_OTA_SIGNAL: R4191.2, R4192.1, U4107.3 (+)
RISE_PROTECTED: R4111.1, R4112.1, U4103.2 (D1)
RISE_REF_TRIM: R4161.2, RV4103.1 (CCW)
RISE_SCALE_TRIM: R4159.2, RV4102.1 (CCW)
RISE_TIME: R4157.1, U4143.13 (-), U4143.14
RISE_TIME_CLAMP: D4105.3 (COM), R4156.2, U4143.12 (+)
RISE_TIME_INV: R4154.2, R4155.2, U4143.9 (-)
RISE_TIME_NEG: R4153.1, R4154.1, U4143.7
RISE_TIME_RAW: R4155.1, R4156.1, U4143.8
RISE_TIME_SUM: R4151.2, R4152.2, R4153.2, U4143.6 (-)
RISE_TIP: J1302.T (Tip), U4103.3 (S1)
SIG_BUFFER: R4117.1, U4146.1, U4146.2 (-), U4147.12 (+)
SIG_GATE: U4112.2, U4113.1, U4113.2
SIG_PROTECTED: R4107.1, R4108.1, U4102.2 (D1)
SIG_TIP: J1301.T (Tip), U4102.3 (S1)
STAGE_FALL: U4111.10, U4124.1, U4124.4, U4124.5
STAGE_FALL_CONTACT: R4130.2, R4131.1, SW1303.3 (Left)
STAGE_HIGH: U4124.11, U4147.10 (+)
START: U4116.3, U4117.4, U4117.5
STG_TIP: J1307.T (Tip), RB4112.2
TOP: U4117.13, U4120.4, U4135.5 (Q)
TOP_LOW: R4144.1, R4147.2, U4109.7, U4112.11
TOP_N: U4116.10, U4135.6 (~Q)
TOP_RAW: U4112.10, U4126.2, U4134.12 (D)
TOP_SYNC: U4134.9 (Q), U4135.2 (D)
TOP_THRESHOLD: R4143.2, R4144.2, U4109.5 (+)
TRIG_ACTIVE: U4111.2, U4113.4, U4113.5
TRIG_CONTACT: R4122.2, R4123.1, SW1304.3 (A), SW1304.4 (A)
