Takazudo/zudo-osc-hole-field/schematic/sheets/filter.kicad_sch

## KiCad design schematic/sheets/filter.kicad_sch (2026-09-30)

Schematic: filter.kicad_sch

Parts:
C2101: 1e-07 F; C0603; MPN GRM188R71H104KA93D
C2102: 1e-06 F; C0603
C2103, C2106, C2109: 1e-10 F; C0603; MPN C0603C101J5GACTU
C2104, C2107, C2110: 1e-11 F; C0603
C2105, C2108, C2111: 1e-08 F; C0603
C2112, C2113: 150 pF C0G; C0603
C2114, C2115: 100 pF; C0603; MPN C0603C101J5GACTU
C2116, C2117, C2118, C2119, C2120, C2121, C2122, C2123, C2124, C2125, C2126, C2127, C2128, C2129, C2130, C2131, C2132, C2133, C2134, C2135, C2136, C2137, C2138, C2139, C2140, C2141, C2142, C2143, C2144, C2145, C2146, C2147, C2148, C2149, C2150, C2151, C2152: 100 nF; C0603; MPN GRM188R71H104KA93D
D601, D602, D603, D604: APHHS1005QWF/D; LED0402-Kingbright-White; MPN APHHS1005QWF/D
D2101, D2102, D2103, D2104, D2105, D2107: BAT54S,215; SOT-23; MPN BAT54S,215
D2106, D2108, D2109, D2110, D2111, D2112, D2113, D2114, D2115, D2116, D2117, D2118, D2119, D2120, D2121, D2122, D2123, D2124, D2125, D2126, D2127, D2128, D2130, D2131, D2132, D2133, D2135, D2136, D2137, D2138, D2140, D2141, D2142, D2143: BAS16GW-QX; SOD-123; MPN BAS16GW-QX
J601, J602, J603, J604, J605, J606, J607, J608: WQP518MA; Jack_3.5mm_QingPu_WQP518MA; MPN WQP518MA
Q2101: BCM847BS,115; SOT-363_SC-70-6; MPN BCM847BS,115
Q2102, Q2103, Q2104, Q2105, Q2106: MMBT3906,215; SOT-23; MPN MMBT3906,215
R2101, R2102, R2108, R2112, R2116, R2120, R2122, R2130, R2138: 10000 Ω; R0603
R2103: 22000 Ω; R0603
R2104, R2125, R2126, R2133, R2134, R2141, R2142: 100000 Ω; R0603; MPN RT0603BRD07100KL
R2105, R2107, R2109, R2111, R2113, R2115, R2117, R2119: 100000 Ω; R0603; MPN RC0603FR-07100KL
R2106, R2110, R2114, R2118, R2123, R2127, R2131, R2135, R2139, R2143: 1000 Ω; R0603
R2121, R2129, R2137: 100 Ω; R0603
R2124, R2128, R2132, R2136, R2140, R2144: 1e+07 Ω; R0603
R2145, R2158: 50 kΩ; R0603
R2146, R2147, R2148, R2149, R2159, R2160, R2161, R2162, R2166, R2170, R2174, R2178, R2179, R2180, R2181, R2182, R2183, R2184, R2186, R2187, R2191, R2192, R2193, R2194, R2195, R2197, R2198: 100 kΩ; R0603; MPN RT0603BRD07100KL
R2150: 1.3 kΩ; R0603
R2151, R2165, R2169, R2173, R2177: 1 kΩ; R0603
R2152: 300 kΩ; R0603
R2153, R2154, R2155, R2190: 22 kΩ; R0603
R2156: 40 kΩ; R0603
R2157, R2185, R2189, R2196: 10 kΩ; R0603
R2163, R2167, R2171, R2175: 200 Ω; R0603
R2164, R2168, R2172, R2176: 470 kΩ; R0603
R2188: 49.9 kΩ; R0603
R2199: 12.4 kΩ; R0603
RB2101: 10 kΩ; R0603
RB2102: 22 kΩ; R0603
RB2103: 330 kΩ; R0603
RB2104: 100 kΩ; R0603; MPN RT0603BRD07100KL
RB2105: 68.1 kΩ; R0603
RB2106, RB2107, RB2108, RB2109, RB2110, RB2111, RB2112, RB2113: 499 Ω; R_1210_3225Metric; MPN RC1210FR-07499RL
RB2114, RB2115, RB2116, RB2117: 5600 Ω; R0603
RV601, RV602, RV605: PTV09A-4020F-B104; PTV09A-4020F; MPN PTV09A-4020F-B104
RV603, RV604, RV606: PTV09A-4020F-B103; PTV09A-4020F; MPN PTV09A-4020F-B103; LCSC C5848782
RV2107: 1 kΩ; Potentiometer_Bourns_TC33X_Vertical; MPN TC33X-2-102E
RV2108: 50 kΩ; Potentiometer_Bourns_TC33X_Vertical
RV2109, RV2110, RV2111, RV2112: 10 kΩ; Potentiometer_Bourns_TC33X_Vertical; MPN TC33X-2-103E
RV2113: 500 kΩ; Potentiometer_Bourns_TC33X_Vertical
U2101: REF5050AIDR; SOIC-8_3.9x4.9mm_P1.27mm; MPN REF5050AIDR; LCSC C27804
U2102, U2103, U2104, U2105: ADG5412FBRUZ; TSSOP-16_4.4x5mm_P0.65mm; MPN ADG5412FBRUZ; LCSC C579073
U2106, U2107: LM13700M/NOPB; SOIC-16_3.9x9.9mm_P1.27mm; MPN LM13700M/NOPB; LCSC C1346265
U2108, U2109: OPA4197IPWR; TSSOP-14_4.4x5mm_P0.65mm; MPN OPA4197IPWR; LCSC C2057327
U2110, U2111, U2112, U2113, U2114, U2115, U2116, U2117, U2118, U2119: OPA4196IDR; SOIC-14_3.9x8.7mm_P1.27mm; MPN OPA4196IDR; LCSC C2057385

Connections:
+5V: R2106.1, R2110.1, R2114.1, R2118.1
+12V: C2101.1, C2116.1, C2117.1, C2119.1, C2121.1, C2123.1, C2125.1, C2127.1, C2129.1, C2131.1, C2133.1, C2135.1, C2137.1, C2139.1, C2141.1, C2143.1, C2145.1, C2147.1, C2149.1, C2151.1, D2101.2 (K), D2102.2 (K), D2103.2 (K), D2104.2 (K), Q2102.2 (E), Q2103.2 (E), Q2104.2 (E), U2101.2 (Vin), U2102.13 (VDD), U2103.13 (VDD), U2104.13 (VDD), U2105.13 (VDD), U2106.11 (V+), U2107.11 (V+), U2108.4 (V+), U2109.4 (V+), U2110.4 (V+), U2111.4 (V+), U2112.4 (V+), U2113.4 (V+), U2114.4 (V+), U2115.4 (V+), U2116.4 (V+), U2117.4 (V+), U2118.4 (V+), U2119.4 (V+)
-12V: C2118.1, C2120.1, C2122.1, C2124.1, C2126.1, C2128.1, C2130.1, C2132.1, C2134.1, C2136.1, C2138.1, C2140.1, C2142.1, C2144.1, C2146.1, C2148.1, C2150.1, C2152.1, D2101.1 (A), D2102.1 (A), D2103.1 (A), D2104.1 (A), U2102.4 (VSS), U2103.4 (VSS), U2104.4 (VSS), U2105.4 (VSS), U2106.6 (V-), U2107.6 (V-), U2108.11 (V-), U2109.11 (V-), U2110.11 (V-), U2111.11 (V-), U2112.11 (V-), U2113.11 (V-), U2114.11 (V-), U2115.11 (V-), U2116.11 (V-), U2117.11 (V-), U2118.11 (V-), U2119.11 (V-)
AGND: C2101.2, C2102.2, C2105.2, C2108.2, C2111.2, C2112.2, C2113.2, C2116.2, C2117.2, C2118.2, C2119.2, C2120.2, C2121.2, C2122.2, C2123.2, C2124.2, C2125.2, C2126.2, C2127.2, C2128.2, C2129.2, C2130.2, C2131.2, C2132.2, C2133.2, C2134.2, C2135.2, C2136.2, C2137.2, C2138.2, C2139.2, C2140.2, C2141.2, C2142.2, C2143.2, C2144.2, C2145.2, C2146.2, C2147.2, C2148.2, C2149.2, C2150.2, C2151.2, C2152.2, D2105.1 (A), D2107.1 (A), J601.S (Sleeve), J602.S (Sleeve), J603.S (Sleeve), J604.S (Sleeve), J605.S (Sleeve), J606.S (Sleeve), J607.S (Sleeve), J608.S (Sleeve), Q2101.2 (B1), R2104.2, R2105.2, R2107.2, R2109.2, R2111.2, R2113.2, R2115.2, R2117.2, R2119.2, R2124.2, R2128.2, R2132.2, R2136.2, R2140.2, R2144.2, R2157.2, R2163.2, R2165.2, R2167.2, R2169.2, R2171.2, R2173.2, R2175.2, R2177.2, R2179.2, RB2114.2, RB2115.2, RB2116.2, RB2117.2, RV601.1 (CCW), RV602.1 (CCW), RV603.1 (CCW), RV604.1 (CCW), RV605.1 (CCW), RV606.1 (CCW), U2101.4 (GND), U2102.5 (GND), U2102.6 (S4), U2102.7 (D4), U2102.8 (IN4), U2102.9 (IN3), U2102.10 (D3), U2102.11 (S3), U2102.14 (S2), U2102.15 (D2), U2102.16 (IN2), U2103.5 (GND), U2103.6 (S4), U2103.7 (D4), U2103.8 (IN4), U2103.9 (IN3), U2103.10 (D3), U2103.11 (S3), U2103.14 (S2), U2103.15 (D2), U2103.16 (IN2), U2104.5 (GND), U2104.6 (S4), U2104.7 (D4), U2104.8 (IN4), U2104.9 (IN3), U2104.10 (D3), U2104.11 (S3), U2104.14 (S2), U2104.15 (D2), U2104.16 (IN2), U2105.5 (GND), U2105.6 (S4), U2105.7 (D4), U2105.8 (IN4), U2105.9 (IN3), U2105.10 (D3), U2105.11 (S3), U2105.14 (S2), U2105.15 (D2), U2105.16 (IN2), U2106.7, U2106.10, U2107.7, U2107.10, U2108.5 (+), U2108.12 (+), U2109.3 (+), U2109.5 (+), U2109.10 (+), U2109.12 (+), U2112.5 (+), U2113.5 (+), U2113.10 (+), U2114.10 (+), U2114.12 (+), U2115.12 (+), U2116.3 (+), U2116.5 (+), U2116.10 (+), U2116.12 (+)
BP_BIAS_SOURCE: Q2103.3 (C), R2154.1
BP_CORE: R2158.1, R2166.1, R2170.1, U2112.13 (-), U2112.14, U2118.5 (+)
BP_IABC: R2154.2, U2106.1
BP_INT: C2112.1, U2106.5, U2112.12 (+)
BP_OFFSET: R2164.2, R2165.1, U2106.4 (-)
BP_OFFSET_TRIM: R2164.1, RV2109.2 (Wiper)
BP_OTA_SIGNAL: R2162.2, R2163.1, U2106.3 (+)
BP_TIP: J606.T (Tip), RB2109.2
C2b02f4_DRIVE: RB2110.1, U2118.8, U2118.9 (-)
C2b02f4_ISO_MID: RB2110.2, RB2111.1
C2b474d_SUM: C2104.2, R2125.2, R2126.2, U2110.6 (-)
C2b474d_W: R2123.1, RV603.2 (WIPER)
C2b474d_W_SENSE: R2123.2, R2124.1, U2110.5 (+)
C3e5421_ENABLE: R2105.1, R2106.2, U2102.1 (IN1)
C5d31c8_DRIVE: RB2106.1, U2118.1, U2118.2 (-)
C5d31c8_ISO_MID: RB2106.2, RB2107.1
C6f9e5f_ENABLE: R2117.1, R2118.2, U2105.1 (IN1)
C7fa4f0_SENSE: D2101.3 (COM), R2108.2, U2117.3 (+)
C8c344f_W: R2135.1, RV602.2 (WIPER)
C8c344f_W_SENSE: C2108.1, R2135.2, R2136.1, U2111.5 (+)
C9dddda_ENABLE: R2109.1, R2110.2, U2103.1 (IN1)
C9fcdd2_DRIVE: D2135.2 (A), D2137.1 (K), U2119.8
C9fcdd2_LED_A: D603.2 (A), D2135.1 (K), D2136.1 (K)
C9fcdd2_LED_K: D603.1 (K), D2137.2 (A), D2138.2 (A)
C9fcdd2_SENSE: D2136.2 (A), D2138.1 (K), RB2116.1, U2119.9 (-)
C11c270_DRIVE: C2109.1, R2137.1, U2111.8
C11c270_FB: C2109.2, R2138.2, U2111.9 (-)
C29cc99_DRIVE: RB2108.1, U2118.6 (-), U2118.7
C29cc99_ISO_MID: RB2108.2, RB2109.1
C56c9d6_DRIVE: RB2112.1, U2118.13 (-), U2118.14
C56c9d6_ISO_MID: RB2112.2, RB2113.1
C835e04_GATE_RAW: R2103.2, R2104.1, U2108.10 (+)
C835e04_GATE_REF: U2108.8, U2108.9 (-)
C835e04_INV: R2101.2, R2102.2, U2108.6 (-)
C835e04_RAW_5V: C2102.1, U2101.6 (Vout), U2108.3 (+)
C945bba_SENSE: D2103.3 (COM), R2116.2, U2117.10 (+)
C14689f_W: R2127.1, RV601.2 (WIPER)
C14689f_W_SENSE: C2105.1, R2127.2, R2128.1, U2110.10 (+)
C72459f_SENSE: D2104.3 (COM), R2120.2, U2117.12 (+)
C85710f_ENABLE: R2113.1, R2114.2, U2104.1 (IN1)
C908572_SENSE: D2102.3 (COM), R2112.2, U2117.5 (+)
CORE_PACK_OPA4196IDR_6_IO_UNUSED2: U2116.6 (-), U2116.7
CORE_PACK_OPA4196IDR_6_IO_UNUSED3: U2116.8, U2116.9 (-)
CORE_PACK_OPA4196IDR_6_IO_UNUSED4: U2116.13 (-), U2116.14
CORE_PACK_OPA4197IPWR_1_IO_UNUSED2: U2109.6 (-), U2109.7
CORE_PACK_OPA4197IPWR_1_IO_UNUSED3: U2109.8, U2109.9 (-)
CORE_PACK_OPA4197IPWR_1_IO_UNUSED4: U2109.13 (-), U2109.14
Ca72ec0_W: R2143.1, RV605.2 (WIPER)
Ca72ec0_W_SENSE: C2111.1, R2143.2, R2144.1, U2112.3 (+)
Cb3b460_SUM: C2110.2, R2141.2, R2142.2, U2111.13 (-)
Cb3b460_W: R2139.1, RV606.2 (WIPER)
Cb3b460_W_SENSE: R2139.2, R2140.1, U2111.12 (+)
Cb3d4a2_DRIVE: D2125.2 (A), D2127.1 (K), U2119.1
Cb3d4a2_LED_A: D601.2 (A), D2125.1 (K), D2126.1 (K)
Cb3d4a2_LED_K: D601.1 (K), D2127.2 (A), D2128.2 (A)
Cb3d4a2_SENSE: D2126.2 (A), D2128.1 (K), RB2114.1, U2119.2 (-)
Cb5b1dc_SUM: C2107.2, R2133.2, R2134.2, U2111.2 (-)
Cb5b1dc_W: R2131.1, RV604.2 (WIPER)
Cb5b1dc_W_SENSE: R2131.2, R2132.1, U2111.3 (+)
Cb6d8fd_DRIVE: D2130.2 (A), D2132.1 (K), U2119.7
Cb6d8fd_LED_A: D602.2 (A), D2130.1 (K), D2131.1 (K)
Cb6d8fd_LED_K: D602.1 (K), D2132.2 (A), D2133.2 (A)
Cb6d8fd_SENSE: D2131.2 (A), D2133.1 (K), RB2115.1, U2119.6 (-)
Cef1e35_DRIVE: C2103.1, R2121.1, U2110.1
Cef1e35_FB: C2103.2, R2122.2, U2110.2 (-)
Cf75ecf_DRIVE: C2106.1, R2129.1, U2110.14
Cf75ecf_FB: C2106.2, R2130.2, U2110.13 (-)
Cfc4b03_DRIVE: D2140.2 (A), D2142.1 (K), U2119.14
Cfc4b03_LED_A: D604.2 (A), D2140.1 (K), D2141.1 (K)
Cfc4b03_LED_K: D604.1 (K), D2142.2 (A), D2143.2 (A)
Cfc4b03_SENSE: D2141.2 (A), D2143.1 (K), RB2117.1, U2119.13 (-)
DRY_BASE: D2108.2 (A), Q2106.1 (B), RB2101.2
DRY_BASE_DRIVE: C2115.1, RB2101.1, U2115.8
DRY_COMMAND: R2197.1, U2115.1, U2115.2 (-)
DRY_CONTROL_CLAMP: D2107.3 (COM), R2196.2, U2115.3 (+)
DRY_CONTROL_INV: R2194.2, R2195.2, U2114.13 (-)
DRY_CONTROL_NEG: R2193.1, R2194.1, U2114.8
DRY_CONTROL_RAW: R2195.1, R2196.1, U2114.14
DRY_CONTROL_SUM: R2191.2, R2192.2, R2193.2, U2114.9 (-)
DRY_CORE: RB2105.1, U2116.1, U2118.12 (+)
DRY_CURRENT: Q2106.3 (C), RB2102.1
DRY_EMITTER: C2115.2, D2108.1 (K), Q2106.2 (E), R2199.2, U2115.9 (-)
DRY_IABC: RB2102.2, U2107.16
DRY_INT: RB2105.2, U2107.12, U2116.2 (-)
DRY_OFFSET: R2176.2, R2177.1, U2107.14 (+)
DRY_OFFSET_TRIM: R2176.1, RV2112.2 (Wiper)
DRY_OTA_SIGNAL: R2174.2, R2175.1, U2107.13 (-)
DRY_TARGET: R2198.1, U2115.7, U2115.10 (+)
DRY_TARGET_SUM: R2197.2, R2198.2, U2115.6 (-)
EXPO_BASE: Q2101.5 (B2), R2151.2
EXPO_COLLECTOR: Q2101.3 (C2), R2153.2
EXPO_COMMAND: R2150.1, R2151.1, U2108.14
EXPO_EMITTER: Q2101.1 (E1), Q2101.4 (E2), U2109.1
EXPO_REFERENCE: Q2101.6 (C1), RV2108.2 (Wiper), RV2108.3 (CW), U2109.2 (-)
EXPO_REF_TRIM: R2152.2, RV2108.1 (CCW)
EXPO_SCALE_SUM: R2149.2, RV2107.2 (Wiper), RV2107.3 (CW), U2108.13 (-)
EXPO_SCALE_TRIM: R2150.2, RV2107.1 (CCW)
FREQ_BUFFER: R2125.1, U2110.3 (+), U2117.6 (-), U2117.7, U2119.5 (+)
FREQ_DEPTH: C2104.1, R2126.1, R2146.1, U2110.7
FREQ_MANUAL: R2145.1, U2110.8, U2110.9 (-)
FREQ_NEG: R2148.1, R2149.1, U2112.7
FREQ_PROTECTED: R2111.1, R2112.1, U2103.2 (D1)
FREQ_REMOTE: R2121.2, R2122.1, RV603.3 (CW)
FREQ_SUM: R2145.2, R2146.2, R2147.2, R2148.2, U2112.6 (-)
FREQ_TIP: J602.T (Tip), U2103.3 (S1)
GAIN_BUFFER: R2141.1, U2111.10 (+), U2117.13 (-), U2117.14, U2119.12 (+)
GAIN_DEPTH: C2110.1, R2142.1, R2192.1, U2111.14
GAIN_MANUAL: R2191.1, U2112.1, U2112.2 (-)
GAIN_PROTECTED: R2119.1, R2120.1, U2105.2 (D1)
GAIN_REMOTE: R2137.2, R2138.1, RV606.3 (CW)
GAIN_TIP: J604.T (Tip), U2105.3 (S1)
HP_CORE: R2161.1, R2162.1, U2112.8, U2118.10 (+)
HP_PLUS: R2156.2, R2157.1, U2112.10 (+)
HP_SUM: R2158.2, R2159.2, R2160.2, R2161.2, U2112.9 (-)
HP_TIP: J607.T (Tip), RB2111.2
IN_BUFFER: R2156.1, R2174.1, U2117.1, U2117.2 (-), U2119.3 (+)
IN_PROTECTED: R2107.1, R2108.1, U2102.2 (D1)
IN_TIP: J601.T (Tip), U2102.3 (S1)
LP_BIAS_SOURCE: Q2104.3 (C), R2155.1
LP_CORE: R2159.1, U2113.1, U2113.2 (-), U2118.3 (+)
LP_IABC: R2155.2, U2106.16
LP_INT: C2113.1, U2106.12, U2113.3 (+)
LP_OFFSET: R2168.2, R2169.1, U2106.13 (-)
LP_OFFSET_TRIM: R2168.1, RV2110.2 (Wiper)
LP_OTA_SIGNAL: R2166.2, R2167.1, U2106.14 (+)
LP_TIP: J605.T (Tip), RB2107.2
MIRROR_BASE: Q2102.1 (B), Q2102.3 (C), Q2103.1 (B), Q2104.1 (B), R2153.1
OUT_TIP: J608.T (Tip), RB2113.2
REF5: D2105.2 (K), D2107.2 (K), R2101.1, R2103.1, R2152.1, R2178.1, R2188.1, R2199.1, RV601.3 (CW), RV602.3 (CW), RV605.3 (CW), RV2109.3 (CW), RV2110.3 (CW), RV2111.3 (CW), RV2112.3 (CW), U2108.1, U2108.2 (-)
REF25: R2178.2, R2179.1, U2114.3 (+), U2115.5 (+)
REFN5: R2102.1, R2147.1, RV2109.1 (CCW), RV2110.1 (CCW), RV2111.1 (CCW), RV2112.1 (CCW), U2108.7
RESONANCE_TRIM: RB2103.2, RV2113.1 (CCW)
RES_BASE: D2106.2 (A), Q2105.1 (B), R2189.2
RES_BASE_DRIVE: C2114.1, R2189.1, U2114.7
RES_BUFFER: R2133.1, U2110.12 (+), U2117.8, U2117.9 (-), U2119.10 (+)
RES_COMMAND: R2186.1, U2113.13 (-), U2113.14
RES_CONTROL_CLAMP: D2105.3 (COM), R2185.2, U2113.12 (+)
RES_CONTROL_INV: R2183.2, R2184.2, U2113.9 (-)
RES_CONTROL_NEG: R2182.1, R2183.1, U2113.7
RES_CONTROL_RAW: R2184.1, R2185.1, U2113.8
RES_CONTROL_SUM: R2180.2, R2181.2, R2182.2, U2113.6 (-)
RES_CURRENT: Q2105.3 (C), R2190.1
RES_DEPTH: C2107.1, R2134.1, R2181.1, U2111.1
RES_EMITTER: C2114.2, D2106.1 (K), Q2105.2 (E), R2188.2, U2114.6 (-)
RES_IABC: R2190.2, U2107.1
RES_INT: D2116.1 (K), D2124.2 (A), RV2113.2 (Wiper), RV2113.3 (CW), U2107.5, U2115.13 (-)
RES_LIMIT: D2109.2 (A), D2117.1 (K), RB2104.2
RES_MANUAL: R2180.1, U2111.6 (-), U2111.7
RES_NEG: R2160.1, RB2103.1, RB2104.1, U2115.14
RES_NEG0: D2117.2 (A), D2118.1 (K)
RES_NEG1: D2118.2 (A), D2119.1 (K)
RES_NEG2: D2119.2 (A), D2120.1 (K)
RES_NEG3: D2120.2 (A), D2121.1 (K)
RES_NEG4: D2121.2 (A), D2122.1 (K)
RES_NEG5: D2122.2 (A), D2123.1 (K)
RES_NEG6: D2123.2 (A), D2124.1 (K)
RES_OFFSET: R2172.2, R2173.1, U2107.4 (-)
RES_OFFSET_TRIM: R2172.1, RV2111.2 (Wiper)
RES_OTA_SIGNAL: R2170.2, R2171.1, U2107.3 (+)
RES_POS0: D2109.1 (K), D2110.2 (A)
RES_POS1: D2110.1 (K), D2111.2 (A)
RES_POS2: D2111.1 (K), D2112.2 (A)
RES_POS3: D2112.1 (K), D2113.2 (A)
RES_POS4: D2113.1 (K), D2114.2 (A)
RES_POS5: D2114.1 (K), D2115.2 (A)
RES_POS6: D2115.1 (K), D2116.2 (A)
RES_PROTECTED: R2115.1, R2116.1, U2104.2 (D1)
RES_REMOTE: R2129.2, R2130.1, RV604.3 (CW)
RES_TARGET: R2187.1, U2114.1, U2114.5 (+)
RES_TARGET_SUM: R2186.2, R2187.2, U2114.2 (-)
RES_TIP: J603.T (Tip), U2104.3 (S1)
