Takazudo/zudo-osc-hole-field/schematic/sheets/manual_ab.kicad_sch

## KiCad design schematic/sheets/manual_ab.kicad_sch (2026-10-02)

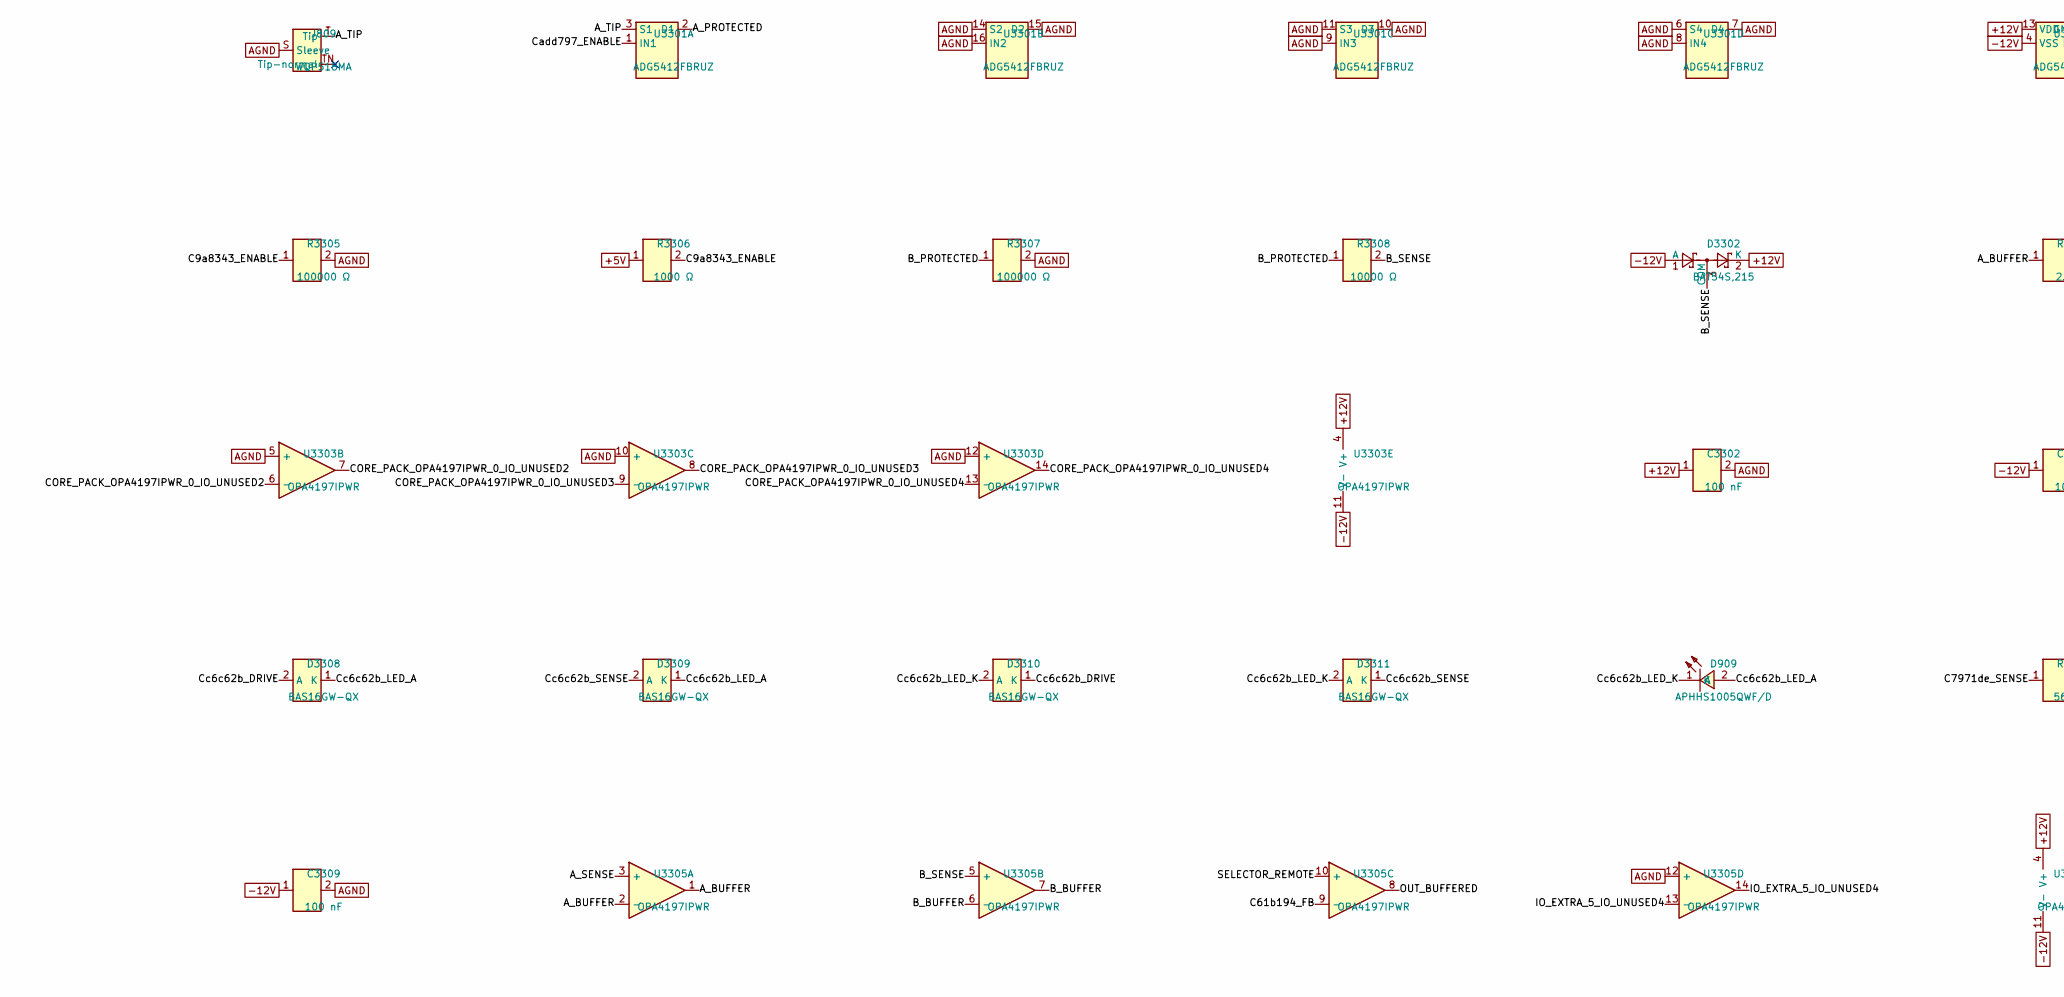
[picture p129: schematic manual_ab.kicad_sch, part in row 1, column 1]

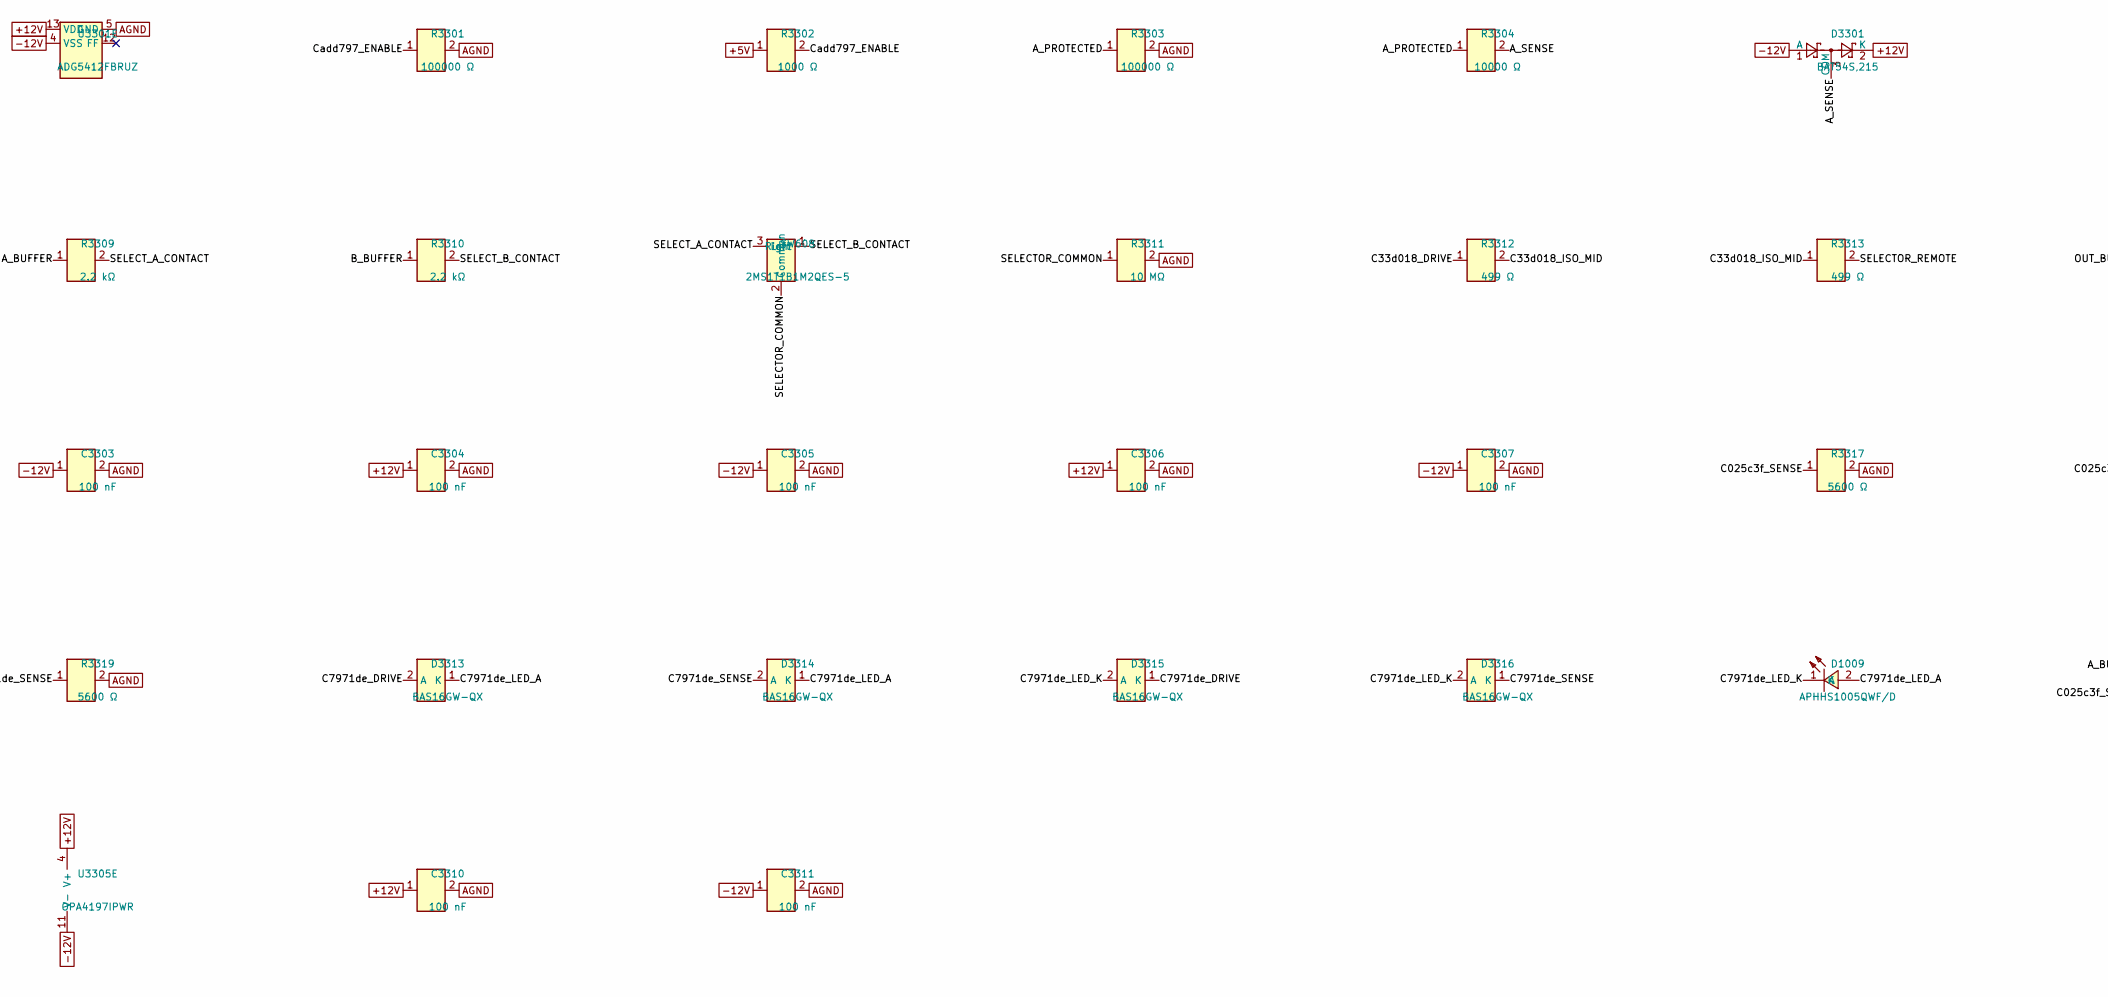
[picture p130: schematic manual_ab.kicad_sch, part in row 1, column 2]

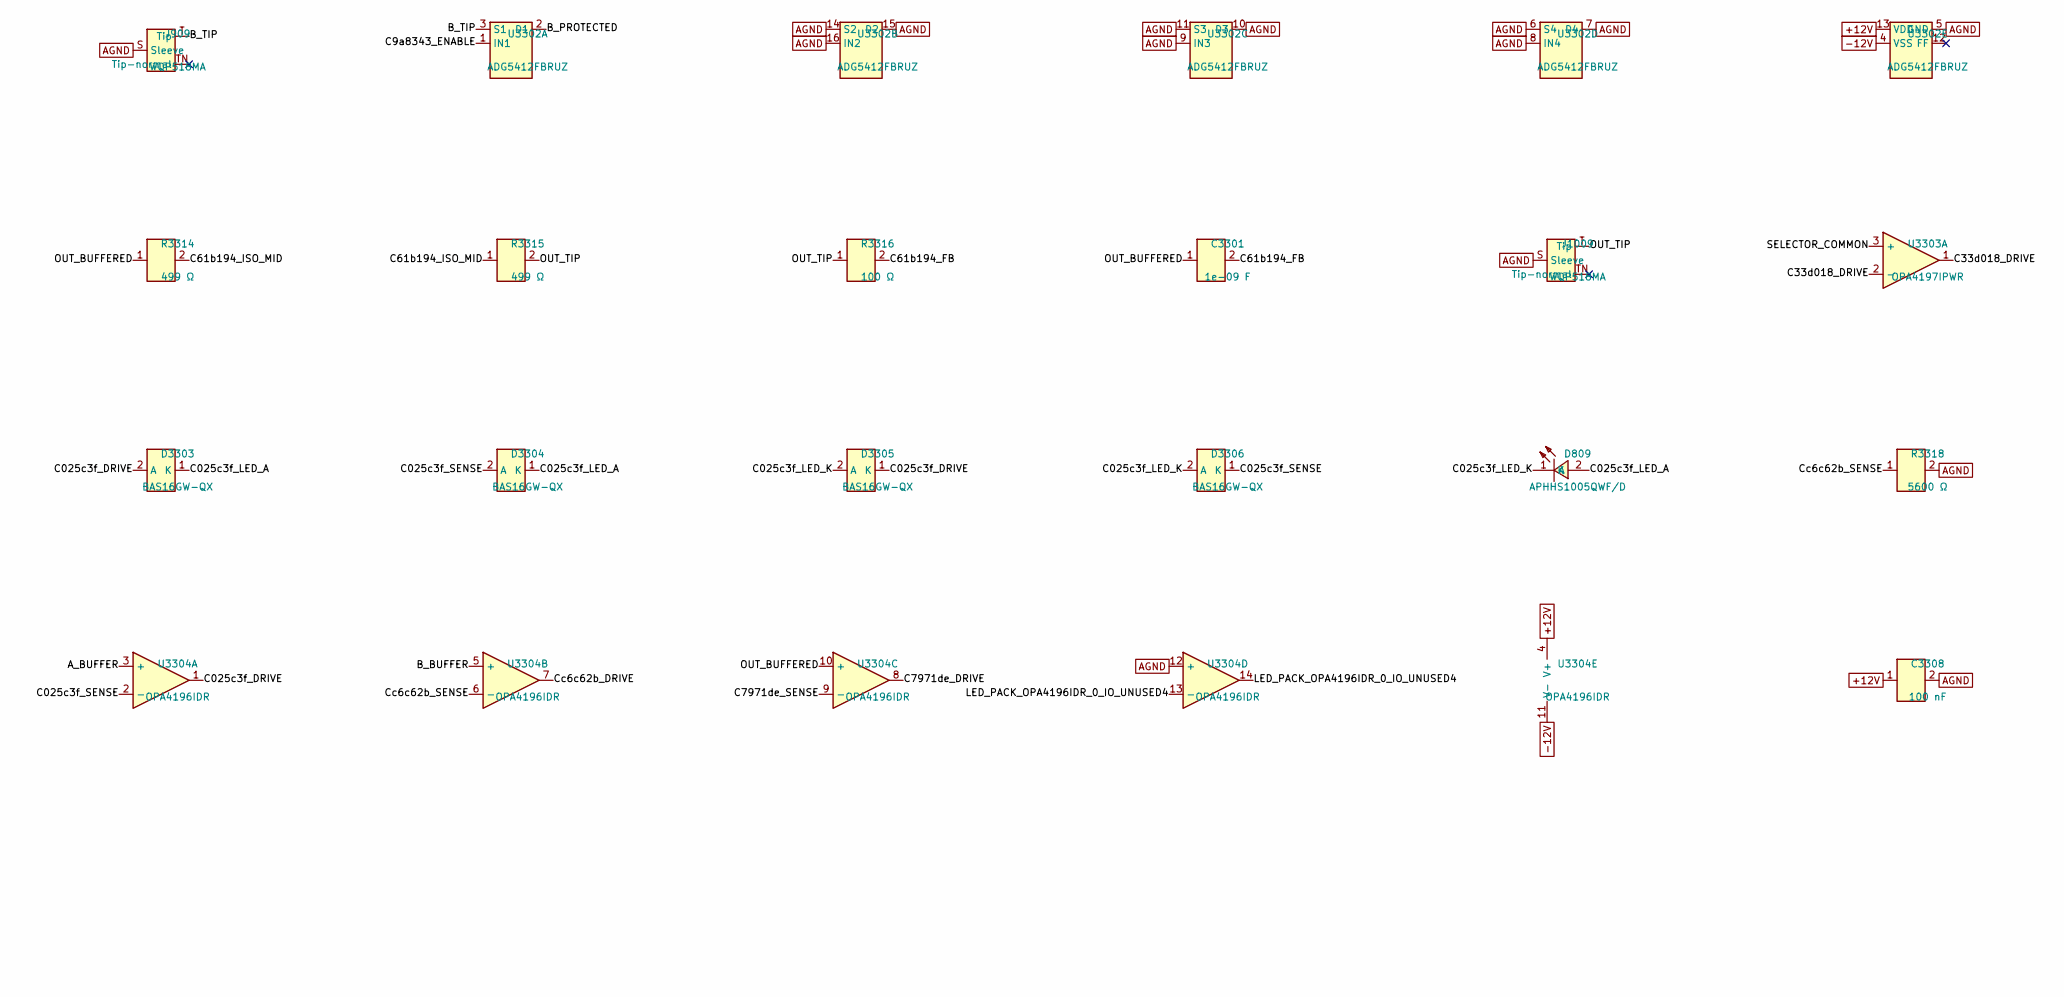
[picture p131: schematic manual_ab.kicad_sch, part in row 1, column 3]

Parts:
C3301: 1e-09 F; C0603; MPN C0603C102J5GACTU
C3302, C3303, C3304, C3305, C3306, C3307, C3308, C3309, C3310, C3311: 100 nF; C0603; MPN GRM188R71H104KA93D
D809, D909, D1009: APHHS1005QWF/D; LED0402-Kingbright-White; MPN APHHS1005QWF/D
D3301, D3302: BAT54S,215; SOT-23; MPN BAT54S,215
D3303, D3304, D3305, D3306, D3308, D3309, D3310, D3311, D3313, D3314, D3315, D3316: BAS16GW-QX; SOD-123; MPN BAS16GW-QX
J809, J909, J1009: WQP518MA; Jack_3.5mm_QingPu_WQP518MA; MPN WQP518MA
R3301, R3303, R3305, R3307: 100000 Ω; R0603; MPN RC0603FR-07100KL
R3302, R3306: 1000 Ω; R0603
R3304, R3308: 10000 Ω; R0603
R3309, R3310: 2.2 kΩ; R0603
R3311: 10 MΩ; R0603
R3312, R3313, R3314, R3315: 499 Ω; R_1210_3225Metric; MPN RC1210FR-07499RL
R3316: 100 Ω; R0603; MPN RC0603FR-07100RL
R3317, R3318, R3319: 5600 Ω; R0603
SW608: 2MS1T1B1M2QES-5; Toggle_Dailywell_2MS_T1B1M2; MPN 2MS1T1B1M2QES-5; LCSC C908280
U3301, U3302: ADG5412FBRUZ; TSSOP-16_4.4x5mm_P0.65mm; MPN ADG5412FBRUZ; LCSC C579073
U3303, U3305: OPA4197IPWR; TSSOP-14_4.4x5mm_P0.65mm; MPN OPA4197IPWR; LCSC C2057327
U3304: OPA4196IDR; SOIC-14_3.9x8.7mm_P1.27mm; MPN OPA4196IDR; LCSC C2057385

Connections:
+5V: R3302.1, R3306.1
+12V: C3302.1, C3304.1, C3306.1, C3308.1, C3310.1, D3301.2 (K), D3302.2 (K), U3301.13 (VDD), U3302.13 (VDD), U3303.4 (V+), U3304.4 (V+), U3305.4 (V+)
-12V: C3303.1, C3305.1, C3307.1, C3309.1, C3311.1, D3301.1 (A), D3302.1 (A), U3301.4 (VSS), U3302.4 (VSS), U3303.11 (V-), U3304.11 (V-), U3305.11 (V-)
AGND: C3302.2, C3303.2, C3304.2, C3305.2, C3306.2, C3307.2, C3308.2, C3309.2, C3310.2, C3311.2, J809.S (Sleeve), J909.S (Sleeve), J1009.S (Sleeve), R3301.2, R3303.2, R3305.2, R3307.2, R3311.2, R3317.2, R3318.2, R3319.2, U3301.5 (GND), U3301.6 (S4), U3301.7 (D4), U3301.8 (IN4), U3301.9 (IN3), U3301.10 (D3), U3301.11 (S3), U3301.14 (S2), U3301.15 (D2), U3301.16 (IN2), U3302.5 (GND), U3302.6 (S4), U3302.7 (D4), U3302.8 (IN4), U3302.9 (IN3), U3302.10 (D3), U3302.11 (S3), U3302.14 (S2), U3302.15 (D2), U3302.16 (IN2), U3303.5 (+), U3303.10 (+), U3303.12 (+), U3304.12 (+), U3305.12 (+)
A_BUFFER: R3309.1, U3304.3 (+), U3305.1, U3305.2 (-)
A_PROTECTED: R3303.1, R3304.1, U3301.2 (D1)
A_SENSE: D3301.3 (COM), R3304.2, U3305.3 (+)
A_TIP: J809.T (Tip), U3301.3 (S1)
B_BUFFER: R3310.1, U3304.5 (+), U3305.6 (-), U3305.7
B_PROTECTED: R3307.1, R3308.1, U3302.2 (D1)
B_SENSE: D3302.3 (COM), R3308.2, U3305.5 (+)
B_TIP: J909.T (Tip), U3302.3 (S1)
C9a8343_ENABLE: R3305.1, R3306.2, U3302.1 (IN1)
C025c3f_DRIVE: D3303.2 (A), D3305.1 (K), U3304.1
C025c3f_LED_A: D809.2 (A), D3303.1 (K), D3304.1 (K)
C025c3f_LED_K: D809.1 (K), D3305.2 (A), D3306.2 (A)
C025c3f_SENSE: D3304.2 (A), D3306.1 (K), R3317.1, U3304.2 (-)
C33d018_DRIVE: R3312.1, U3303.1, U3303.2 (-)
C33d018_ISO_MID: R3312.2, R3313.1
C61b194_FB: C3301.2, R3316.2, U3305.9 (-)
C61b194_ISO_MID: R3314.2, R3315.1
C7971de_DRIVE: D3313.2 (A), D3315.1 (K), U3304.8
C7971de_LED_A: D1009.2 (A), D3313.1 (K), D3314.1 (K)
C7971de_LED_K: D1009.1 (K), D3315.2 (A), D3316.2 (A)
C7971de_SENSE: D3314.2 (A), D3316.1 (K), R3319.1, U3304.9 (-)
CORE_PACK_OPA4197IPWR_0_IO_UNUSED2: U3303.6 (-), U3303.7
CORE_PACK_OPA4197IPWR_0_IO_UNUSED3: U3303.8, U3303.9 (-)
CORE_PACK_OPA4197IPWR_0_IO_UNUSED4: U3303.13 (-), U3303.14
Cadd797_ENABLE: R3301.1, R3302.2, U3301.1 (IN1)
Cc6c62b_DRIVE: D3308.2 (A), D3310.1 (K), U3304.7
Cc6c62b_LED_A: D909.2 (A), D3308.1 (K), D3309.1 (K)
Cc6c62b_LED_K: D909.1 (K), D3310.2 (A), D3311.2 (A)
Cc6c62b_SENSE: D3309.2 (A), D3311.1 (K), R3318.1, U3304.6 (-)
IO_EXTRA_5_IO_UNUSED4: U3305.13 (-), U3305.14
LED_PACK_OPA4196IDR_0_IO_UNUSED4: U3304.13 (-), U3304.14
OUT_BUFFERED: C3301.1, R3314.1, U3304.10 (+), U3305.8
OUT_TIP: J1009.T (Tip), R3315.2, R3316.1
SELECTOR_COMMON: R3311.1, SW608.2 (Common), U3303.3 (+)
SELECTOR_REMOTE: R3313.2, U3305.10 (+)
SELECT_A_CONTACT: R3309.2, SW608.3 (Left)
SELECT_B_CONTACT: R3310.2, SW608.1 (Right)
