Takazudo/zudo-osc-hole-field/schematic/sheets/mix4_vca.kicad_sch

## KiCad design schematic/sheets/mix4_vca.kicad_sch (2026-09-30)

Schematic: mix4_vca.kicad_sch

Parts:
C8301: 1e-07 F; C0603; MPN GRM188R71H104KA93D
C8302: 1e-06 F; C0603
C8303, C8305, C8307, C8309, C8311: 1e-10 F; C0603; MPN C0603C101J5GACTU
C8304, C8306, C8308, C8310, C8312: 1e-11 F; C0603
C8313: 1e-08 F; C0603
C8314: 100 pF; C0603; MPN C0603C101J5GACTU
C8315, C8316, C8317, C8318, C8319, C8320, C8321, C8322, C8323, C8324, C8325, C8326, C8327, C8328, C8329, C8330, C8331, C8332, C8333, C8334, C8335, C8336, C8337, C8338, C8339, C8340, C8341, C8342, C8343, C8344, C8345, C8346, C8347, C8348, C8349, C8350, C8351: 100 nF; C0603; MPN GRM188R71H104KA93D
D1101, D1102, D1103, D1104, D1105, D1106: APHHS1005QWF/D; LED0402-Kingbright-White; MPN APHHS1005QWF/D
D8308, D8309, D8310, D8311, D8312, D8313: BAT54S,215; SOT-23; MPN BAT54S,215
D8314, D8315, D8316, D8317, D8318, D8319, D8320, D8321, D8322, D8323, D8324, D8325, D8326, D8327, D8328, D8329, D8330, D8331, D8332, D8333, D8334, D8335, D8336, D8337, D8338: BAS16GW-QX; SOD-123; MPN BAS16GW-QX
D11061: APG1005SEC/E-T; LED0402-Kingbright-Red; MPN APG1005SEC/E-T
J1101, J1102, J1103, J1104, J1105, J1106: WQP518MA; Jack_3.5mm_QingPu_WQP518MA; MPN WQP518MA
Q8301: MMBT3906,215; SOT-23; MPN MMBT3906,215
R8301, R8302, R8308, R8310, R8318, R8320, R8328, R8330, R8338, R8340, R8353, R8355: 10000 Ω; R0603
R8303: 22000 Ω; R0603
R8304, R8313, R8314, R8323, R8324, R8333, R8334, R8343, R8344, R8358, R8359, R8389, R8390: 100000 Ω; R0603; MPN RT0603BRD07100KL
R8305, R8307, R8315, R8317, R8325, R8327, R8335, R8337, R8350, R8352: 100000 Ω; R0603; MPN RC0603FR-07100KL
R8306, R8311, R8316, R8321, R8326, R8331, R8336, R8341, R8351, R8356, R8360: 1000 Ω; R0603
R8309, R8319, R8329, R8339, R8354, R8376: 100 Ω; R0603
R8312, R8322, R8332, R8342, R8357, R8361: 1e+07 Ω; R0603
R8345, R8346, R8347, R8348, R8362, R8363, R8364, R8365, R8366, R8368, R8369, R8370, R8371, R8375, R8379, R8380: 100 kΩ; R0603; MPN RT0603BRD07100KL
R8349: 50 kΩ; R0603
R8367, R8372, R8373, R8374: 10 kΩ; R0603
R8377: 1 MΩ; R0603
R8378: 1 kΩ; R0603
R8381, R8382: 499 Ω; R_1210_3225Metric; MPN RC1210FR-07499RL
R8383, R8384, R8385, R8386, R8387, R8388: 5600 Ω; R0603
R8391: 22100 Ω; R0603
RV1101, RV1102, RV1103, RV1104, RV1105: PTV09A-4020F-B103; PTV09A-4020F; MPN PTV09A-4020F-B103; LCSC C5848782
RV1106: PTV09A-4020F-B104; PTV09A-4020F; MPN PTV09A-4020F-B104
RV8307, RV8308: 10 kΩ; Potentiometer_Bourns_TC33X_Vertical; MPN TC33X-2-103E
U8301: REF5050AIDR; SOIC-8_3.9x4.9mm_P1.27mm; MPN REF5050AIDR; LCSC C27804
U8302, U8303, U8304, U8305, U8306: ADG5412FBRUZ; TSSOP-16_4.4x5mm_P0.65mm; MPN ADG5412FBRUZ; LCSC C579073
U8307: LM13700M/NOPB; SOIC-16_3.9x9.9mm_P1.27mm; MPN LM13700M/NOPB; LCSC C1346265
U8308: OPA4197IPWR; TSSOP-14_4.4x5mm_P0.65mm; MPN OPA4197IPWR; LCSC C2057327
U8309, U8310, U8311, U8312, U8313, U8314, U8317, U8318, U8319: OPA4196IDR; SOIC-14_3.9x8.7mm_P1.27mm; MPN OPA4196IDR; LCSC C2057385
U8315, U8316: LM393BIDR; SOIC-8_3.9x4.9mm_P1.27mm; MPN LM393BIDR

Connections:
1_BUFFER: R8313.1, U8309.3 (+), U8314.1, U8314.2 (-)
1_GAIN: C8304.1, R8314.1, R8345.1, U8309.7, U8317.10 (+)
1_PROTECTED: R8307.1, R8308.1, U8302.2 (D1)
1_REMOTE: R8309.2, R8310.1, RV1101.3 (CW)
1_TIP: J1101.T (Tip), U8302.3 (S1)
2_BUFFER: R8323.1, U8309.10 (+), U8314.6 (-), U8314.7
2_GAIN: C8306.1, R8324.1, R8346.1, U8309.14, U8317.12 (+)
2_PROTECTED: R8317.1, R8318.1, U8303.2 (D1)
2_REMOTE: R8319.2, R8320.1, RV1102.3 (CW)
2_TIP: J1102.T (Tip), U8303.3 (S1)
3_BUFFER: R8333.1, U8310.3 (+), U8314.8, U8314.9 (-)
3_GAIN: C8308.1, R8334.1, R8347.1, U8310.7, U8318.3 (+)
3_PROTECTED: R8327.1, R8328.1, U8304.2 (D1)
3_REMOTE: R8329.2, R8330.1, RV1103.3 (CW)
3_TIP: J1103.T (Tip), U8304.3 (S1)
4_BUFFER: R8343.1, U8310.10 (+), U8314.13 (-), U8314.14
4_GAIN: C8310.1, R8344.1, R8348.1, U8310.14, U8318.5 (+)
4_PROTECTED: R8337.1, R8338.1, U8305.2 (D1)
4_REMOTE: R8339.2, R8340.1, RV1104.3 (CW)
4_TIP: J1104.T (Tip), U8305.3 (S1)
+5V: R8306.1, R8316.1, R8326.1, R8336.1, R8351.1, U8315.6 (-), U8316.6 (-)
+12V: C8301.1, C8315.1, C8316.1, C8318.1, C8320.1, C8322.1, C8324.1, C8326.1, C8328.1, C8330.1, C8332.1, C8334.1, C8336.1, C8338.1, C8340.1, C8342.1, C8344.1, C8346.1, C8348.1, C8350.1, D8308.2 (K), D8309.2 (K), D8310.2 (K), D8311.2 (K), D8312.2 (K), R8391.1, U8301.2 (Vin), U8302.13 (VDD), U8303.13 (VDD), U8304.13 (VDD), U8305.13 (VDD), U8306.13 (VDD), U8307.11 (V+), U8308.4 (V+), U8309.4 (V+), U8310.4 (V+), U8311.4 (V+), U8312.4 (V+), U8313.4 (V+), U8314.4 (V+), U8315.8 (V+), U8316.8 (V+), U8317.4 (V+), U8318.4 (V+), U8319.4 (V+)
-12V: C8317.1, C8319.1, C8321.1, C8323.1, C8325.1, C8327.1, C8329.1, C8331.1, C8333.1, C8335.1, C8337.1, C8339.1, C8341.1, C8343.1, C8345.1, C8347.1, C8349.1, C8351.1, D8308.1 (A), D8309.1 (A), D8310.1 (A), D8311.1 (A), D8312.1 (A), R8379.2, U8302.4 (VSS), U8303.4 (VSS), U8304.4 (VSS), U8305.4 (VSS), U8306.4 (VSS), U8307.6 (V-), U8308.11 (V-), U8309.11 (V-), U8310.11 (V-), U8311.11 (V-), U8312.11 (V-), U8313.11 (V-), U8314.11 (V-), U8315.4 (GND), U8316.4 (GND), U8317.11 (V-), U8318.11 (V-), U8319.11 (V-)
AGND: C8301.2, C8302.2, C8313.2, C8315.2, C8316.2, C8317.2, C8318.2, C8319.2, C8320.2, C8321.2, C8322.2, C8323.2, C8324.2, C8325.2, C8326.2, C8327.2, C8328.2, C8329.2, C8330.2, C8331.2, C8332.2, C8333.2, C8334.2, C8335.2, C8336.2, C8337.2, C8338.2, C8339.2, C8340.2, C8341.2, C8342.2, C8343.2, C8344.2, C8345.2, C8346.2, C8347.2, C8348.2, C8349.2, C8350.2, C8351.2, D8313.1 (A), J1101.S (Sleeve), J1102.S (Sleeve), J1103.S (Sleeve), J1104.S (Sleeve), J1105.S (Sleeve), J1106.S (Sleeve), R8304.2, R8305.2, R8307.2, R8312.2, R8315.2, R8317.2, R8322.2, R8325.2, R8327.2, R8332.2, R8335.2, R8337.2, R8342.2, R8350.2, R8352.2, R8357.2, R8361.2, R8369.2, R8376.2, R8378.2, R8383.2, R8384.2, R8385.2, R8386.2, R8387.2, R8388.2, R8390.2, RV1101.1 (CCW), RV1102.1 (CCW), RV1103.1 (CCW), RV1104.1 (CCW), RV1105.1 (CCW), RV1106.1 (CCW), U8301.4 (GND), U8302.5 (GND), U8302.6 (S4), U8302.7 (D4), U8302.8 (IN4), U8302.9 (IN3), U8302.10 (D3), U8302.11 (S3), U8302.14 (S2), U8302.15 (D2), U8302.16 (IN2), U8303.5 (GND), U8303.6 (S4), U8303.7 (D4), U8303.8 (IN4), U8303.9 (IN3), U8303.10 (D3), U8303.11 (S3), U8303.14 (S2), U8303.15 (D2), U8303.16 (IN2), U8304.5 (GND), U8304.6 (S4), U8304.7 (D4), U8304.8 (IN4), U8304.9 (IN3), U8304.10 (D3), U8304.11 (S3), U8304.14 (S2), U8304.15 (D2), U8304.16 (IN2), U8305.5 (GND), U8305.6 (S4), U8305.7 (D4), U8305.8 (IN4), U8305.9 (IN3), U8305.10 (D3), U8305.11 (S3), U8305.14 (S2), U8305.15 (D2), U8305.16 (IN2), U8306.5 (GND), U8306.6 (S4), U8306.7 (D4), U8306.8 (IN4), U8306.9 (IN3), U8306.10 (D3), U8306.11 (S3), U8306.14 (S2), U8306.15 (D2), U8306.16 (IN2), U8307.7, U8307.10, U8307.13 (-), U8307.14 (+), U8308.5 (+), U8308.12 (+), U8311.3 (+), U8312.3 (+), U8312.5 (+), U8313.5 (+), U8313.10 (+), U8313.12 (+), U8315.5 (+), U8316.5 (+), U8319.5 (+), U8319.10 (+), U8319.12 (+)
ATTEN_BUFFER: R8358.1, U8311.5 (+), U8317.1, U8317.2 (-), U8318.10 (+)
ATTEN_PROTECTED: R8352.1, R8353.1, U8306.2 (D1)
ATTEN_REMOTE: R8354.2, R8355.1, RV1105.3 (CW)
ATTEN_TIP: J1105.T (Tip), U8306.3 (S1)
BASE: D8314.2 (A), Q8301.1 (B), R8373.2
BASE_DRIVE: C8314.1, R8373.1, U8313.1
C1c45d6_W: R8360.1, RV1106.2 (WIPER)
C1c45d6_W_SENSE: C8313.1, R8360.2, R8361.1, U8311.12 (+)
C2b7337_ENABLE: R8350.1, R8351.2, U8306.1 (IN1)
C2be340_SENSE: D8311.3 (COM), R8338.2, U8314.12 (+)
C5eb398_SENSE: D8309.3 (COM), R8318.2, U8314.5 (+)
C24ce01_SUM: C8312.2, R8358.2, R8359.2, U8311.9 (-)
C24ce01_W: R8356.1, RV1105.2 (WIPER)
C24ce01_W_SENSE: R8356.2, R8357.1, U8311.10 (+)
C75c2e7_SUM: C8304.2, R8313.2, R8314.2, U8309.6 (-)
C75c2e7_W: R8311.1, RV1101.2 (WIPER)
C75c2e7_W_SENSE: R8311.2, R8312.1, U8309.5 (+)
C93bba0_DRIVE: D8319.2 (A), D8321.1 (K), U8317.14
C93bba0_LED_A: D1102.2 (A), D8319.1 (K), D8320.1 (K)
C93bba0_LED_K: D1102.1 (K), D8321.2 (A), D8322.2 (A)
C93bba0_SENSE: D8320.2 (A), D8322.1 (K), R8384.1, U8317.13 (-)
C412fd1_DRIVE: D8315.2 (A), D8317.1 (K), U8317.8
C412fd1_LED_A: D1101.2 (A), D8315.1 (K), D8316.1 (K)
C412fd1_LED_K: D1101.1 (K), D8317.2 (A), D8318.2 (A)
C412fd1_SENSE: D8316.2 (A), D8318.1 (K), R8383.1, U8317.9 (-)
C865f36_DRIVE: C8309.1, R8339.1, U8310.8
C865f36_FB: C8309.2, R8340.2, U8310.9 (-)
C2006b9_DRIVE: C8307.1, R8329.1, U8310.1
C2006b9_FB: C8307.2, R8330.2, U8310.2 (-)
C2169e5_DRIVE: D8323.2 (A), D8325.1 (K), U8318.1
C2169e5_LED_A: D1103.2 (A), D8323.1 (K), D8324.1 (K)
C2169e5_LED_K: D1103.1 (K), D8325.2 (A), D8326.2 (A)
C2169e5_SENSE: D8324.2 (A), D8326.1 (K), R8385.1, U8318.2 (-)
C3848b5_ENABLE: R8315.1, R8316.2, U8303.1 (IN1)
C7750d4_SENSE: D8310.3 (COM), R8328.2, U8314.10 (+)
C8321d8_BUF: R8389.1, U8319.1, U8319.2 (-)
C8321d8_CLIP_N: D11061.1 (K), U8315.1, U8316.1
C8321d8_HALF: R8389.2, R8390.1, U8315.2 (-), U8316.3 (+)
C8321d8_LED_A: D11061.2 (A), R8391.2
C38051c_SUM: C8308.2, R8333.2, R8334.2, U8310.6 (-)
C38051c_W: R8331.1, RV1103.2 (WIPER)
C38051c_W_SENSE: R8331.2, R8332.1, U8310.5 (+)
C72128a_ENABLE: R8305.1, R8306.2, U8302.1 (IN1)
C154038_SUM: C8310.2, R8343.2, R8344.2, U8310.13 (-)
C154038_W: R8341.1, RV1104.2 (WIPER)
C154038_W_SENSE: R8341.2, R8342.1, U8310.12 (+)
C320656_DRIVE: D8331.2 (A), D8333.1 (K), U8318.8
C320656_LED_A: D1105.2 (A), D8331.1 (K), D8332.1 (K)
C320656_LED_K: D1105.1 (K), D8333.2 (A), D8334.2 (A)
C320656_SENSE: D8332.2 (A), D8334.1 (K), R8387.1, U8318.9 (-)
C797803_DRIVE: C8303.1, R8309.1, U8309.1
C797803_FB: C8303.2, R8310.2, U8309.2 (-)
COMMAND: R8370.1, U8312.8, U8312.9 (-)
COMMAND_CLAMP: D8313.3 (COM), R8367.2, U8312.10 (+)
COMMAND_INVERT_SUM: R8365.2, R8366.2, U8312.6 (-)
COMMAND_NEG: R8364.1, R8365.1, U8312.1
COMMAND_RAW: R8366.1, R8367.1, U8312.7
COMMAND_SUM: R8362.2, R8363.2, R8364.2, U8312.2 (-)
CURRENT_SOURCE: Q8301.3 (C), R8374.1
CV_DEPTH: C8312.1, R8359.1, R8363.1, U8311.8
Ca1191c_SUM: C8306.2, R8323.2, R8324.2, U8309.13 (-)
Ca1191c_W: R8321.1, RV1102.2 (WIPER)
Ca1191c_W_SENSE: R8321.2, R8322.1, U8309.12 (+)
Caeced9_SENSE: D8308.3 (COM), R8308.2, U8314.3 (+)
Cb5ae41_SENSE: D8312.3 (COM), R8353.2, U8317.3 (+)
Cc98f53_ENABLE: R8325.1, R8326.2, U8304.1 (IN1)
Ccb7527_DRIVE: C8311.1, R8354.1, U8311.7
Ccb7527_FB: C8311.2, R8355.2, U8311.6 (-)
Cd90fa0_GATE_RAW: R8303.2, R8304.1, U8308.10 (+)
Cd90fa0_GATE_REF: U8308.8, U8308.9 (-)
Cd90fa0_INV: R8301.2, R8302.2, U8308.6 (-)
Cd90fa0_RAW_5V: C8302.1, U8301.6 (Vout), U8308.3 (+)
Cd59875_DRIVE: D8335.2 (A), D8337.1 (K), U8318.14
Cd59875_LED_A: D1106.2 (A), D8335.1 (K), D8336.1 (K)
Cd59875_LED_K: D1106.1 (K), D8337.2 (A), D8338.2 (A)
Cd59875_SENSE: D8336.2 (A), D8338.1 (K), R8388.1, U8318.13 (-)
Cea264a_DRIVE: R8381.1, U8317.6 (-), U8317.7
Cea264a_ISO_MID: R8381.2, R8382.1
Cf876de_DRIVE: D8327.2 (A), D8329.1 (K), U8318.7
Cf876de_LED_A: D1104.2 (A), D8327.1 (K), D8328.1 (K)
Cf876de_LED_K: D1104.1 (K), D8329.2 (A), D8330.2 (A)
Cf876de_SENSE: D8328.2 (A), D8330.1 (K), R8386.1, U8318.6 (-)
Cfaa69a_DRIVE: C8305.1, R8319.1, U8309.8
Cfaa69a_FB: C8305.2, R8320.2, U8309.9 (-)
Cfd8558_ENABLE: R8335.1, R8336.2, U8305.1 (IN1)
EMITTER: C8314.2, D8314.1 (K), Q8301.2 (E), R8372.2, U8313.2 (-)
EMITTER_TARGET: R8371.1, U8312.14, U8313.3 (+)
G1_PACK_OPA4196IDR_4_IO_UNUSED3: U8313.8, U8313.9 (-)
G1_PACK_OPA4196IDR_4_IO_UNUSED4: U8313.13 (-), U8313.14
G1_PACK_OPA4197IPWR_0_IO_UNUSED4: U8308.13 (-), U8308.14
IABC1: R8374.2, U8307.1
IABC2: R8379.1, U8307.16
IO_EXTRA_19_IO_UNUSED2: U8319.6 (-), U8319.7
IO_EXTRA_19_IO_UNUSED3: U8319.8, U8319.9 (-)
IO_EXTRA_19_IO_UNUSED4: U8319.13 (-), U8319.14
LEVEL_MANUAL: R8362.1, U8311.13 (-), U8311.14
OFFSET_W: R8377.1, RV8307.2 (Wiper)
OTA_CURRENT: RV8308.2 (Wiper), RV8308.3 (CW), U8307.5, U8313.6 (-)
OTA_OFFSET: R8377.2, R8378.1, U8307.4 (-)
OTA_SIGNAL: R8375.2, R8376.1, U8307.3 (+)
REF5: D8313.2 (K), R8301.1, R8303.1, R8368.1, R8372.1, RV1106.3 (CW), RV8307.3 (CW), U8308.1, U8308.2 (-), U8315.3 (+)
REF25: R8368.2, R8369.1, U8312.12 (+)
REFN5: R8302.1, RV8307.1 (CCW), U8308.7, U8316.2 (-)
SUM_NODE: R8345.2, R8346.2, R8347.2, R8348.2, R8349.2, U8311.2 (-)
SUM_POSTVCA: R8380.1, U8313.7, U8317.5 (+), U8318.12 (+)
SUM_PRELEVEL: R8349.1, R8375.1, U8311.1, U8319.3 (+)
SUM_TIP: J1106.T (Tip), R8382.2
TARGET_SUM: R8370.2, R8371.2, U8312.13 (-)
TIA_TRIM: R8380.2, RV8308.1 (CCW)
