Takazudo/zudo-osc-hole-field/schematic/sheets/mix5.kicad_sch

## KiCad design schematic/sheets/mix5.kicad_sch (2026-09-30)

Schematic: mix5.kicad_sch

Parts:
C8101: 1e-07 F; C0603; MPN GRM188R71H104KA93D
C8102: 1e-06 F; C0603
C8103, C8105, C8107, C8109, C8111, C8113: 1e-10 F; C0603; MPN C0603C101J5GACTU
C8104, C8106, C8108, C8110, C8112: 1e-11 F; C0603
C8114, C8115, C8116, C8117, C8118, C8119, C8120, C8121, C8122, C8123, C8124, C8125, C8126, C8127, C8128, C8129, C8130, C8131, C8132, C8133, C8134, C8135, C8136, C8137, C8138, C8139, C8140, C8141, C8142, C8143, C8144, C8145, C8146: 100 nF; C0603; MPN GRM188R71H104KA93D
D901, D902, D903, D904, D905, D906: APHHS1005QWF/D; LED0402-Kingbright-White; MPN APHHS1005QWF/D
D8108, D8109, D8110, D8111, D8112: BAT54S,215; SOT-23; MPN BAT54S,215
D8113, D8114, D8115, D8116, D8117, D8118, D8119, D8120, D8121, D8122, D8123, D8124, D8125, D8126, D8127, D8128, D8129, D8130, D8131, D8132, D8133, D8134, D8135, D8136: BAS16GW-QX; SOD-123; MPN BAS16GW-QX
D9061: APG1005SEC/E-T; LED0402-Kingbright-Red; MPN APG1005SEC/E-T
J901, J902, J903, J904, J905, J906: WQP518MA; Jack_3.5mm_QingPu_WQP518MA; MPN WQP518MA
R8101, R8102, R8108, R8110, R8118, R8120, R8128, R8130, R8138, R8140, R8148, R8150, R8162: 10000 Ω; R0603
R8103: 22000 Ω; R0603
R8104, R8113, R8114, R8123, R8124, R8133, R8134, R8143, R8144, R8153, R8154, R8175, R8176: 100000 Ω; R0603; MPN RT0603BRD07100KL
R8105, R8107, R8115, R8117, R8125, R8127, R8135, R8137, R8145, R8147: 100000 Ω; R0603; MPN RC0603FR-07100KL
R8106, R8111, R8116, R8121, R8126, R8131, R8136, R8141, R8146, R8151, R8163: 1000 Ω; R0603
R8109, R8119, R8129, R8139, R8149, R8161: 100 Ω; R0603
R8112, R8122, R8132, R8142, R8152, R8164: 1e+07 Ω; R0603
R8155, R8156, R8157, R8158, R8159, R8165, R8166: 100 kΩ; R0603; MPN RT0603BRD07100KL
R8160: 40 kΩ; R0603
R8167, R8168: 499 Ω; R_1210_3225Metric; MPN RC1210FR-07499RL
R8169, R8170, R8171, R8172, R8173, R8174: 5600 Ω; R0603
R8177: 22100 Ω; R0603
RV901, RV902, RV903, RV904, RV905, RV906: PTV09A-4020F-B103; PTV09A-4020F; MPN PTV09A-4020F-B103; LCSC C5848782
U8101: REF5050AIDR; SOIC-8_3.9x4.9mm_P1.27mm; MPN REF5050AIDR; LCSC C27804
U8102, U8103, U8104, U8105, U8106: ADG5412FBRUZ; TSSOP-16_4.4x5mm_P0.65mm; MPN ADG5412FBRUZ; LCSC C579073
U8107: OPA4197IPWR; TSSOP-14_4.4x5mm_P0.65mm; MPN OPA4197IPWR; LCSC C2057327
U8108, U8109, U8110, U8111, U8112, U8115, U8116, U8117: OPA4196IDR; SOIC-14_3.9x8.7mm_P1.27mm; MPN OPA4196IDR; LCSC C2057385
U8113, U8114: LM393BIDR; SOIC-8_3.9x4.9mm_P1.27mm; MPN LM393BIDR

Connections:
1_BUFFER: R8113.1, U8108.3 (+), U8112.1, U8112.2 (-)
1_GAIN: C8104.1, R8114.1, R8155.1, U8108.7, U8115.10 (+)
1_PROTECTED: R8107.1, R8108.1, U8102.2 (D1)
1_REMOTE: R8109.2, R8110.1, RV901.3 (CW)
1_TIP: J901.T (Tip), U8102.3 (S1)
2_BUFFER: R8123.1, U8108.10 (+), U8112.6 (-), U8112.7
2_GAIN: C8106.1, R8124.1, R8156.1, U8108.14, U8115.12 (+)
2_PROTECTED: R8117.1, R8118.1, U8103.2 (D1)
2_REMOTE: R8119.2, R8120.1, RV902.3 (CW)
2_TIP: J902.T (Tip), U8103.3 (S1)
3_BUFFER: R8133.1, U8109.3 (+), U8112.8, U8112.9 (-)
3_GAIN: C8108.1, R8134.1, R8157.1, U8109.7, U8116.3 (+)
3_PROTECTED: R8127.1, R8128.1, U8104.2 (D1)
3_REMOTE: R8129.2, R8130.1, RV903.3 (CW)
3_TIP: J903.T (Tip), U8104.3 (S1)
4_BUFFER: R8143.1, U8109.10 (+), U8112.13 (-), U8112.14
4_GAIN: C8110.1, R8144.1, R8158.1, U8109.14, U8116.5 (+)
4_PROTECTED: R8137.1, R8138.1, U8105.2 (D1)
4_REMOTE: R8139.2, R8140.1, RV904.3 (CW)
4_TIP: J904.T (Tip), U8105.3 (S1)
5_BUFFER: R8153.1, U8110.3 (+), U8115.1, U8115.2 (-)
5_GAIN: C8112.1, R8154.1, R8159.1, U8110.7, U8116.10 (+)
5_PROTECTED: R8147.1, R8148.1, U8106.2 (D1)
5_REMOTE: R8149.2, R8150.1, RV905.3 (CW)
5_TIP: J905.T (Tip), U8106.3 (S1)
+5V: R8106.1, R8116.1, R8126.1, R8136.1, R8146.1, U8113.6 (-), U8114.6 (-)
+12V: C8101.1, C8114.1, C8115.1, C8117.1, C8119.1, C8121.1, C8123.1, C8125.1, C8127.1, C8129.1, C8131.1, C8133.1, C8135.1, C8137.1, C8139.1, C8141.1, C8143.1, C8145.1, D8108.2 (K), D8109.2 (K), D8110.2 (K), D8111.2 (K), D8112.2 (K), R8177.1, U8101.2 (Vin), U8102.13 (VDD), U8103.13 (VDD), U8104.13 (VDD), U8105.13 (VDD), U8106.13 (VDD), U8107.4 (V+), U8108.4 (V+), U8109.4 (V+), U8110.4 (V+), U8111.4 (V+), U8112.4 (V+), U8113.8 (V+), U8114.8 (V+), U8115.4 (V+), U8116.4 (V+), U8117.4 (V+)
-12V: C8116.1, C8118.1, C8120.1, C8122.1, C8124.1, C8126.1, C8128.1, C8130.1, C8132.1, C8134.1, C8136.1, C8138.1, C8140.1, C8142.1, C8144.1, C8146.1, D8108.1 (A), D8109.1 (A), D8110.1 (A), D8111.1 (A), D8112.1 (A), U8102.4 (VSS), U8103.4 (VSS), U8104.4 (VSS), U8105.4 (VSS), U8106.4 (VSS), U8107.11 (V-), U8108.11 (V-), U8109.11 (V-), U8110.11 (V-), U8111.11 (V-), U8112.11 (V-), U8113.4 (GND), U8114.4 (GND), U8115.11 (V-), U8116.11 (V-), U8117.11 (V-)
AGND: C8101.2, C8102.2, C8114.2, C8115.2, C8116.2, C8117.2, C8118.2, C8119.2, C8120.2, C8121.2, C8122.2, C8123.2, C8124.2, C8125.2, C8126.2, C8127.2, C8128.2, C8129.2, C8130.2, C8131.2, C8132.2, C8133.2, C8134.2, C8135.2, C8136.2, C8137.2, C8138.2, C8139.2, C8140.2, C8141.2, C8142.2, C8143.2, C8144.2, C8145.2, C8146.2, J901.S (Sleeve), J902.S (Sleeve), J903.S (Sleeve), J904.S (Sleeve), J905.S (Sleeve), J906.S (Sleeve), R8104.2, R8105.2, R8107.2, R8112.2, R8115.2, R8117.2, R8122.2, R8125.2, R8127.2, R8132.2, R8135.2, R8137.2, R8142.2, R8145.2, R8147.2, R8152.2, R8164.2, R8169.2, R8170.2, R8171.2, R8172.2, R8173.2, R8174.2, R8176.2, RV901.1 (CCW), RV902.1 (CCW), RV903.1 (CCW), RV904.1 (CCW), RV905.1 (CCW), RV906.1 (CCW), U8101.4 (GND), U8102.5 (GND), U8102.6 (S4), U8102.7 (D4), U8102.8 (IN4), U8102.9 (IN3), U8102.10 (D3), U8102.11 (S3), U8102.14 (S2), U8102.15 (D2), U8102.16 (IN2), U8103.5 (GND), U8103.6 (S4), U8103.7 (D4), U8103.8 (IN4), U8103.9 (IN3), U8103.10 (D3), U8103.11 (S3), U8103.14 (S2), U8103.15 (D2), U8103.16 (IN2), U8104.5 (GND), U8104.6 (S4), U8104.7 (D4), U8104.8 (IN4), U8104.9 (IN3), U8104.10 (D3), U8104.11 (S3), U8104.14 (S2), U8104.15 (D2), U8104.16 (IN2), U8105.5 (GND), U8105.6 (S4), U8105.7 (D4), U8105.8 (IN4), U8105.9 (IN3), U8105.10 (D3), U8105.11 (S3), U8105.14 (S2), U8105.15 (D2), U8105.16 (IN2), U8106.5 (GND), U8106.6 (S4), U8106.7 (D4), U8106.8 (IN4), U8106.9 (IN3), U8106.10 (D3), U8106.11 (S3), U8106.14 (S2), U8106.15 (D2), U8106.16 (IN2), U8107.5 (+), U8107.12 (+), U8110.10 (+), U8111.5 (+), U8111.10 (+), U8111.12 (+), U8113.5 (+), U8114.5 (+), U8117.5 (+), U8117.10 (+), U8117.12 (+)
C0abe44_SENSE: D8111.3 (COM), R8138.2, U8112.12 (+)
C0f3556_W: R8163.1, RV906.2 (WIPER)
C0f3556_W_SENSE: R8163.2, R8164.1, U8111.3 (+)
C1cfef8_ENABLE: R8105.1, R8106.2, U8102.1 (IN1)
C1ea714_DRIVE: D8133.2 (A), D8135.1 (K), U8116.14
C1ea714_LED_A: D906.2 (A), D8133.1 (K), D8134.1 (K)
C1ea714_LED_K: D906.1 (K), D8135.2 (A), D8136.2 (A)
C1ea714_SENSE: D8134.2 (A), D8136.1 (K), R8174.1, U8116.13 (-)
C2c2153_SUM: C8104.2, R8113.2, R8114.2, U8108.6 (-)
C2c2153_W: R8111.1, RV901.2 (WIPER)
C2c2153_W_SENSE: R8111.2, R8112.1, U8108.5 (+)
C02cf7e_DRIVE: R8167.1, U8115.6 (-), U8115.7
C02cf7e_ISO_MID: R8167.2, R8168.1
C3c322e_DRIVE: D8113.2 (A), D8115.1 (K), U8115.8
C3c322e_LED_A: D901.2 (A), D8113.1 (K), D8114.1 (K)
C3c322e_LED_K: D901.1 (K), D8115.2 (A), D8116.2 (A)
C3c322e_SENSE: D8114.2 (A), D8116.1 (K), R8169.1, U8115.9 (-)
C3d7d3c_DRIVE: D8117.2 (A), D8119.1 (K), U8115.14
C3d7d3c_LED_A: D902.2 (A), D8117.1 (K), D8118.1 (K)
C3d7d3c_LED_K: D902.1 (K), D8119.2 (A), D8120.2 (A)
C3d7d3c_SENSE: D8118.2 (A), D8120.1 (K), R8170.1, U8115.13 (-)
C5ea6dc_ENABLE: R8115.1, R8116.2, U8103.1 (IN1)
C6a2619_BUF: R8175.1, U8117.1, U8117.2 (-)
C6a2619_CLIP_N: D9061.1 (K), U8113.1, U8114.1
C6a2619_HALF: R8175.2, R8176.1, U8113.2 (-), U8114.3 (+)
C6a2619_LED_A: D9061.2 (A), R8177.2
C8e3cbc_ENABLE: R8125.1, R8126.2, U8104.1 (IN1)
C81f845_ENABLE: R8145.1, R8146.2, U8106.1 (IN1)
C222c99_GATE_RAW: R8103.2, R8104.1, U8107.10 (+)
C222c99_GATE_REF: U8107.8, U8107.9 (-)
C222c99_INV: R8101.2, R8102.2, U8107.6 (-)
C222c99_RAW_5V: C8102.1, U8101.6 (Vout), U8107.3 (+)
C674b06_SENSE: D8109.3 (COM), R8118.2, U8112.5 (+)
C3716d7_ENABLE: R8135.1, R8136.2, U8105.1 (IN1)
C6236f5_DRIVE: D8121.2 (A), D8123.1 (K), U8116.1
C6236f5_LED_A: D903.2 (A), D8121.1 (K), D8122.1 (K)
C6236f5_LED_K: D903.1 (K), D8123.2 (A), D8124.2 (A)
C6236f5_SENSE: D8122.2 (A), D8124.1 (K), R8171.1, U8116.2 (-)
C8568b9_SENSE: D8108.3 (COM), R8108.2, U8112.3 (+)
C060458_DRIVE: C8103.1, R8109.1, U8108.1
C060458_FB: C8103.2, R8110.2, U8108.2 (-)
C81714b_DRIVE: C8109.1, R8139.1, U8109.8
C81714b_FB: C8109.2, R8140.2, U8109.9 (-)
C445167_SUM: C8108.2, R8133.2, R8134.2, U8109.6 (-)
C445167_W: R8131.1, RV903.2 (WIPER)
C445167_W_SENSE: R8131.2, R8132.1, U8109.5 (+)
C819409_SENSE: D8112.3 (COM), R8148.2, U8115.3 (+)
Ca0a275_DRIVE: C8111.1, R8149.1, U8110.1
Ca0a275_FB: C8111.2, R8150.2, U8110.2 (-)
Ca92eeb_SUM: C8106.2, R8123.2, R8124.2, U8108.13 (-)
Ca92eeb_W: R8121.1, RV902.2 (WIPER)
Ca92eeb_W_SENSE: R8121.2, R8122.1, U8108.12 (+)
Cb4cecc_DRIVE: C8105.1, R8119.1, U8108.8
Cb4cecc_FB: C8105.2, R8120.2, U8108.9 (-)
Cb103af_SUM: C8112.2, R8153.2, R8154.2, U8110.6 (-)
Cb103af_W: R8151.1, RV905.2 (WIPER)
Cb103af_W_SENSE: R8151.2, R8152.1, U8110.5 (+)
Cc95daa_DRIVE: C8107.1, R8129.1, U8109.1
Cc95daa_FB: C8107.2, R8130.2, U8109.2 (-)
Ce3bd71_SENSE: D8110.3 (COM), R8128.2, U8112.10 (+)
Ce6323c_DRIVE: C8113.1, R8161.1, U8110.14
Ce6323c_FB: C8113.2, R8162.2, U8110.13 (-)
Ce67982_SUM: C8110.2, R8143.2, R8144.2, U8109.13 (-)
Ce67982_W: R8141.1, RV904.2 (WIPER)
Ce67982_W_SENSE: R8141.2, R8142.1, U8109.12 (+)
Cf1bc56_DRIVE: D8125.2 (A), D8127.1 (K), U8116.7
Cf1bc56_LED_A: D904.2 (A), D8125.1 (K), D8126.1 (K)
Cf1bc56_LED_K: D904.1 (K), D8127.2 (A), D8128.2 (A)
Cf1bc56_SENSE: D8126.2 (A), D8128.1 (K), R8172.1, U8116.6 (-)
Cf07a81_DRIVE: D8129.2 (A), D8131.1 (K), U8116.8
Cf07a81_LED_A: D905.2 (A), D8129.1 (K), D8130.1 (K)
Cf07a81_LED_K: D905.1 (K), D8131.2 (A), D8132.2 (A)
Cf07a81_SENSE: D8130.2 (A), D8132.1 (K), R8173.1, U8116.9 (-)
G1_PACK_OPA4196IDR_3_IO_UNUSED3: U8111.8, U8111.9 (-)
G1_PACK_OPA4196IDR_3_IO_UNUSED4: U8111.13 (-), U8111.14
G1_PACK_OPA4197IPWR_0_IO_UNUSED4: U8107.13 (-), U8107.14
IO_EXTRA_17_IO_UNUSED2: U8117.6 (-), U8117.7
IO_EXTRA_17_IO_UNUSED3: U8117.8, U8117.9 (-)
IO_EXTRA_17_IO_UNUSED4: U8117.13 (-), U8117.14
LEVEL_BUFFERED: R8165.1, U8111.1, U8111.2 (-)
LEVEL_REMOTE: R8161.2, R8162.1, RV906.3 (CW)
REF5: R8101.1, R8103.1, U8107.1, U8107.2 (-), U8113.3 (+)
REFN5: R8102.1, U8107.7, U8114.2 (-)
RESTORE_SUM: R8165.2, R8166.2, U8111.6 (-)
SUM_NODE: R8155.2, R8156.2, R8157.2, R8158.2, R8159.2, R8160.2, U8110.9 (-)
SUM_POSTLEVEL: R8166.1, U8111.7, U8115.5 (+), U8116.12 (+)
SUM_PRELEVEL: R8160.1, U8110.8, U8110.12 (+), U8117.3 (+)
SUM_TIP: J906.T (Tip), R8168.2
