Takazudo/zudo-osc-hole-field/schematic/sheets/mult.kicad_sch

## KiCad design schematic/sheets/mult.kicad_sch (2026-10-02)

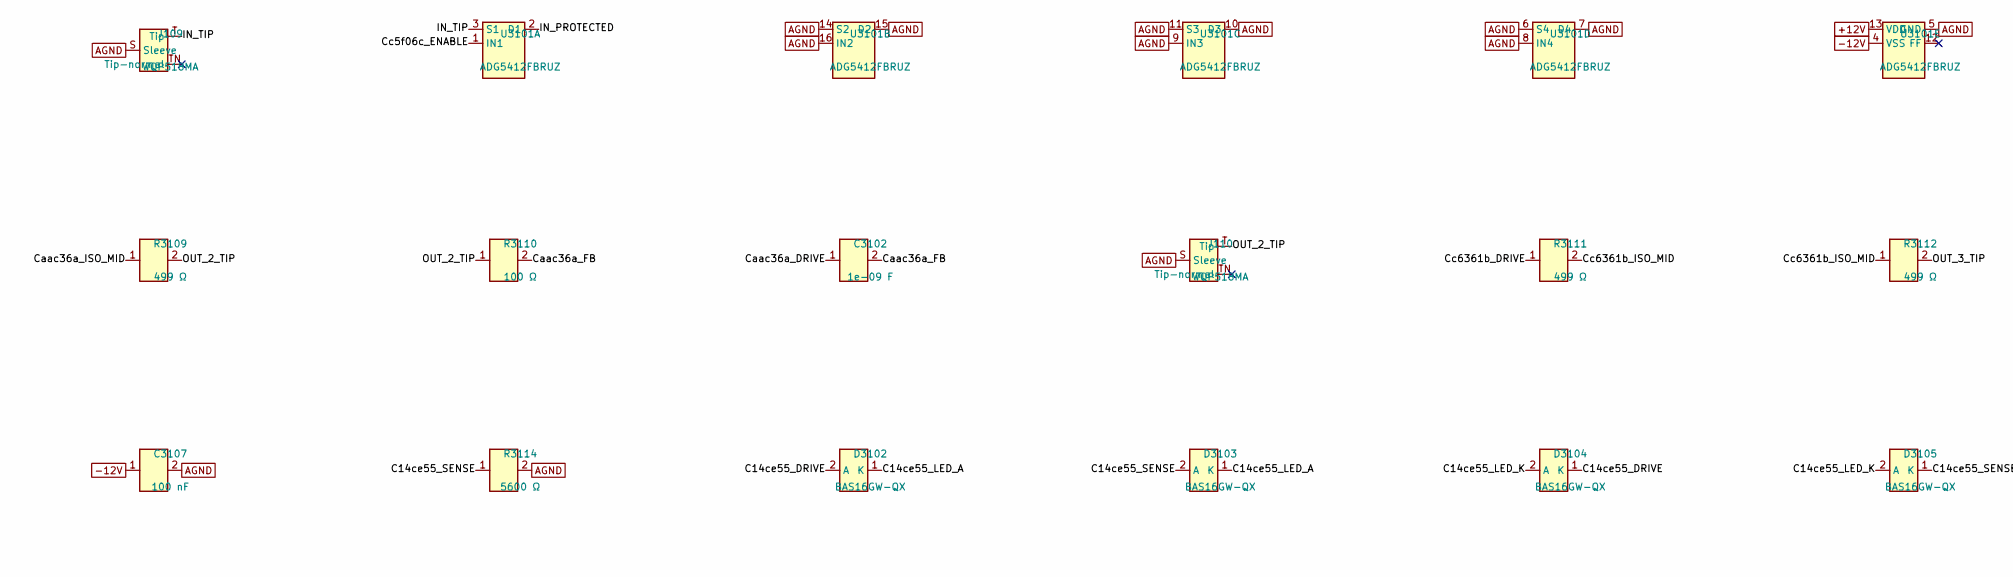
[picture p132: schematic mult.kicad_sch, part in row 1, column 1]

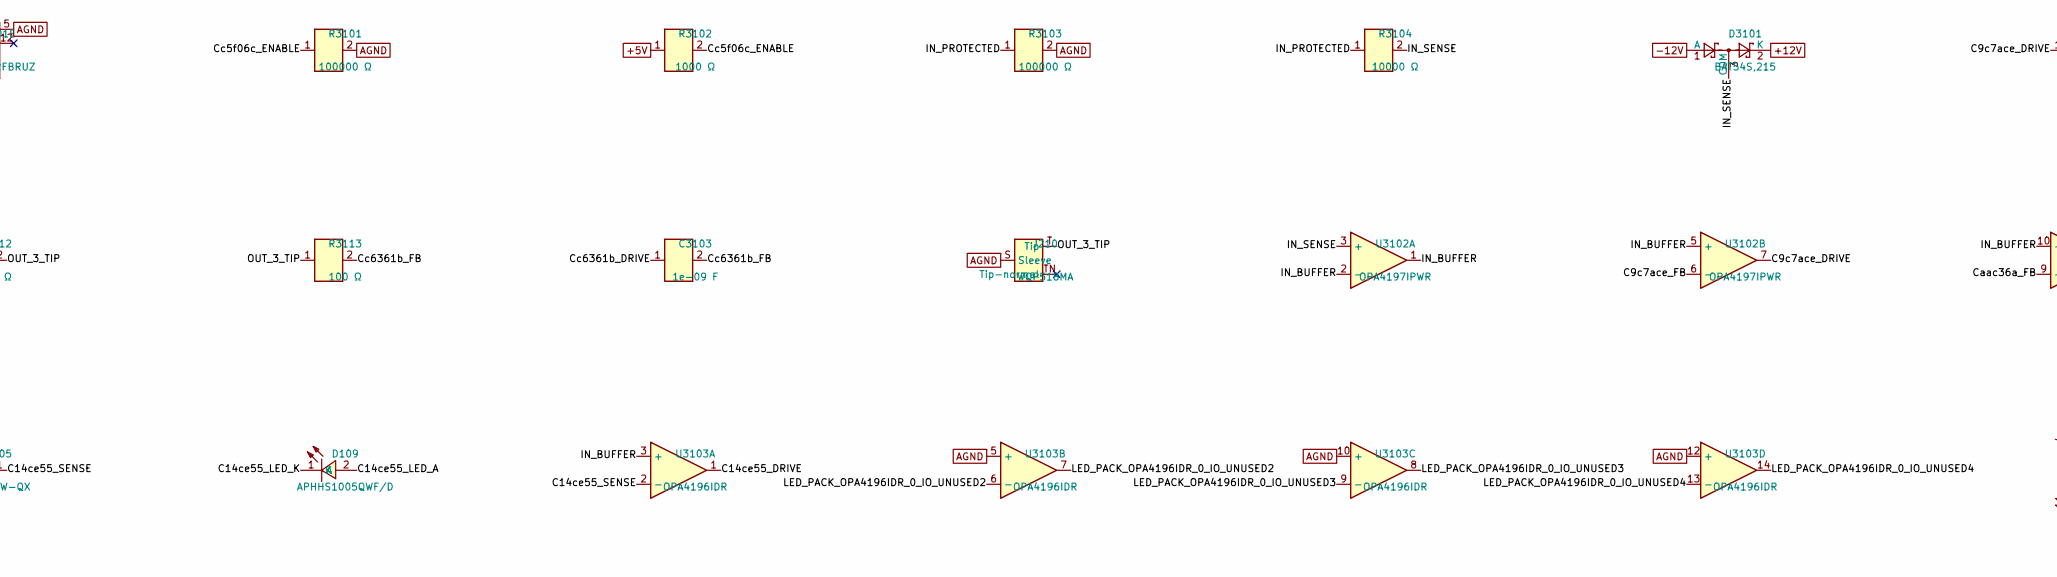
[picture p133: schematic mult.kicad_sch, part in row 1, column 2]

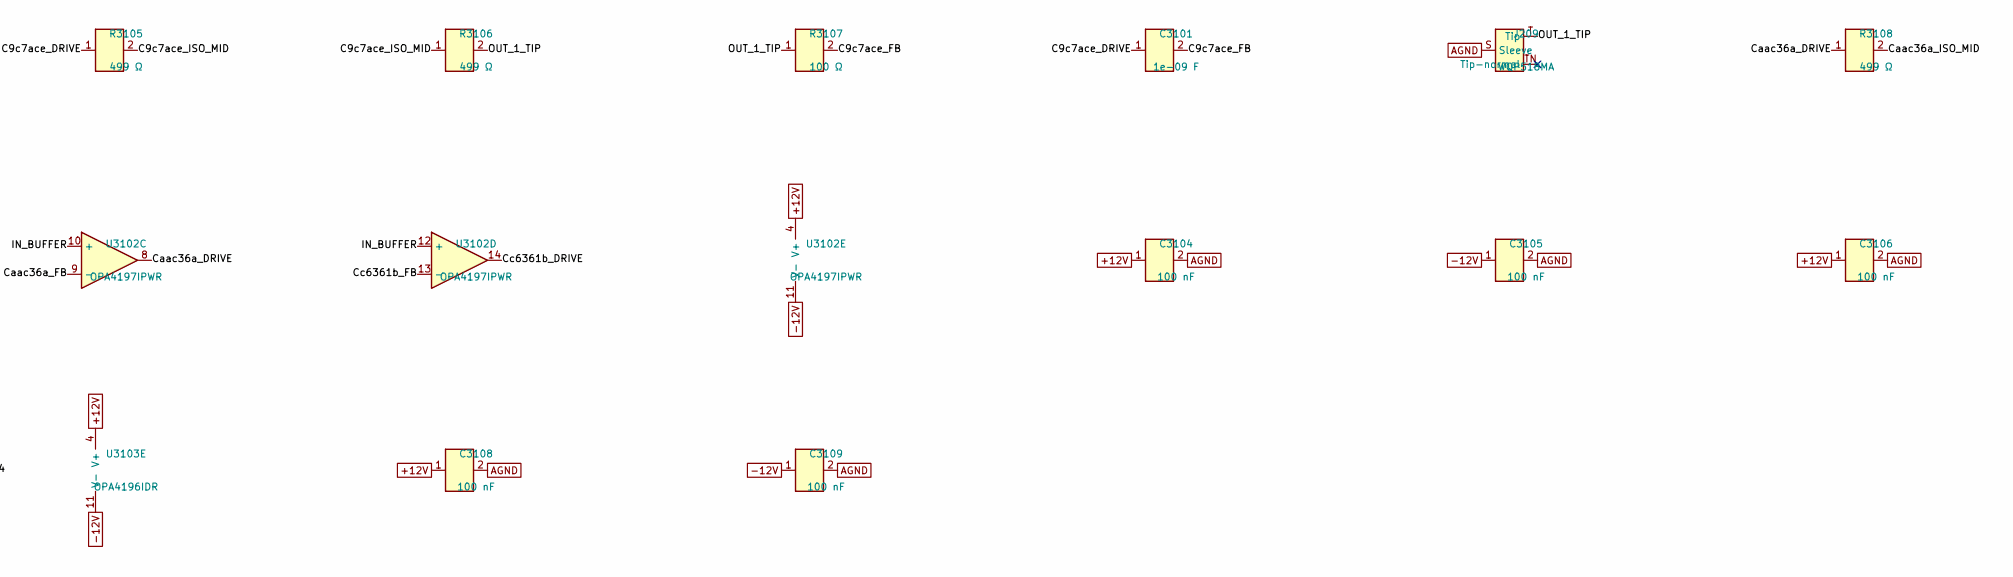
[picture p134: schematic mult.kicad_sch, part in row 1, column 3]

Parts:
C3101, C3102, C3103: 1e-09 F; C0603; MPN C0603C102J5GACTU
C3104, C3105, C3106, C3107, C3108, C3109: 100 nF; C0603; MPN GRM188R71H104KA93D
D109: APHHS1005QWF/D; LED0402-Kingbright-White; MPN APHHS1005QWF/D
D3101: BAT54S,215; SOT-23; MPN BAT54S,215
D3102, D3103, D3104, D3105: BAS16GW-QX; SOD-123; MPN BAS16GW-QX
J109, J110, J209, J210: WQP518MA; Jack_3.5mm_QingPu_WQP518MA; MPN WQP518MA
R3101, R3103: 100000 Ω; R0603; MPN RC0603FR-07100KL
R3102: 1000 Ω; R0603
R3104: 10000 Ω; R0603
R3105, R3106, R3108, R3109, R3111, R3112: 499 Ω; R_1210_3225Metric; MPN RC1210FR-07499RL
R3107, R3110, R3113: 100 Ω; R0603; MPN RC0603FR-07100RL
R3114: 5600 Ω; R0603
U3101: ADG5412FBRUZ; TSSOP-16_4.4x5mm_P0.65mm; MPN ADG5412FBRUZ; LCSC C579073
U3102: OPA4197IPWR; TSSOP-14_4.4x5mm_P0.65mm; MPN OPA4197IPWR; LCSC C2057327
U3103: OPA4196IDR; SOIC-14_3.9x8.7mm_P1.27mm; MPN OPA4196IDR; LCSC C2057385

Connections:
+5V: R3102.1
+12V: C3104.1, C3106.1, C3108.1, D3101.2 (K), U3101.13 (VDD), U3102.4 (V+), U3103.4 (V+)
-12V: C3105.1, C3107.1, C3109.1, D3101.1 (A), U3101.4 (VSS), U3102.11 (V-), U3103.11 (V-)
AGND: C3104.2, C3105.2, C3106.2, C3107.2, C3108.2, C3109.2, J109.S (Sleeve), J110.S (Sleeve), J209.S (Sleeve), J210.S (Sleeve), R3101.2, R3103.2, R3114.2, U3101.5 (GND), U3101.6 (S4), U3101.7 (D4), U3101.8 (IN4), U3101.9 (IN3), U3101.10 (D3), U3101.11 (S3), U3101.14 (S2), U3101.15 (D2), U3101.16 (IN2), U3103.5 (+), U3103.10 (+), U3103.12 (+)
C9c7ace_DRIVE: C3101.1, R3105.1, U3102.7
C9c7ace_FB: C3101.2, R3107.2, U3102.6 (-)
C9c7ace_ISO_MID: R3105.2, R3106.1
C14ce55_DRIVE: D3102.2 (A), D3104.1 (K), U3103.1
C14ce55_LED_A: D109.2 (A), D3102.1 (K), D3103.1 (K)
C14ce55_LED_K: D109.1 (K), D3104.2 (A), D3105.2 (A)
C14ce55_SENSE: D3103.2 (A), D3105.1 (K), R3114.1, U3103.2 (-)
Caac36a_DRIVE: C3102.1, R3108.1, U3102.8
Caac36a_FB: C3102.2, R3110.2, U3102.9 (-)
Caac36a_ISO_MID: R3108.2, R3109.1
Cc5f06c_ENABLE: R3101.1, R3102.2, U3101.1 (IN1)
Cc6361b_DRIVE: C3103.1, R3111.1, U3102.14
Cc6361b_FB: C3103.2, R3113.2, U3102.13 (-)
Cc6361b_ISO_MID: R3111.2, R3112.1
IN_BUFFER: U3102.1, U3102.2 (-), U3102.5 (+), U3102.10 (+), U3102.12 (+), U3103.3 (+)
IN_PROTECTED: R3103.1, R3104.1, U3101.2 (D1)
IN_SENSE: D3101.3 (COM), R3104.2, U3102.3 (+)
IN_TIP: J109.T (Tip), U3101.3 (S1)
LED_PACK_OPA4196IDR_0_IO_UNUSED2: U3103.6 (-), U3103.7
LED_PACK_OPA4196IDR_0_IO_UNUSED3: U3103.8, U3103.9 (-)
LED_PACK_OPA4196IDR_0_IO_UNUSED4: U3103.13 (-), U3103.14
OUT_1_TIP: J209.T (Tip), R3106.2, R3107.1
OUT_2_TIP: J110.T (Tip), R3109.2, R3110.1
OUT_3_TIP: J210.T (Tip), R3112.2, R3113.1
