Takazudo/zudo-osc-hole-field/schematic/sheets/noise.kicad_sch

## KiCad design schematic/sheets/noise.kicad_sch (2026-09-30)

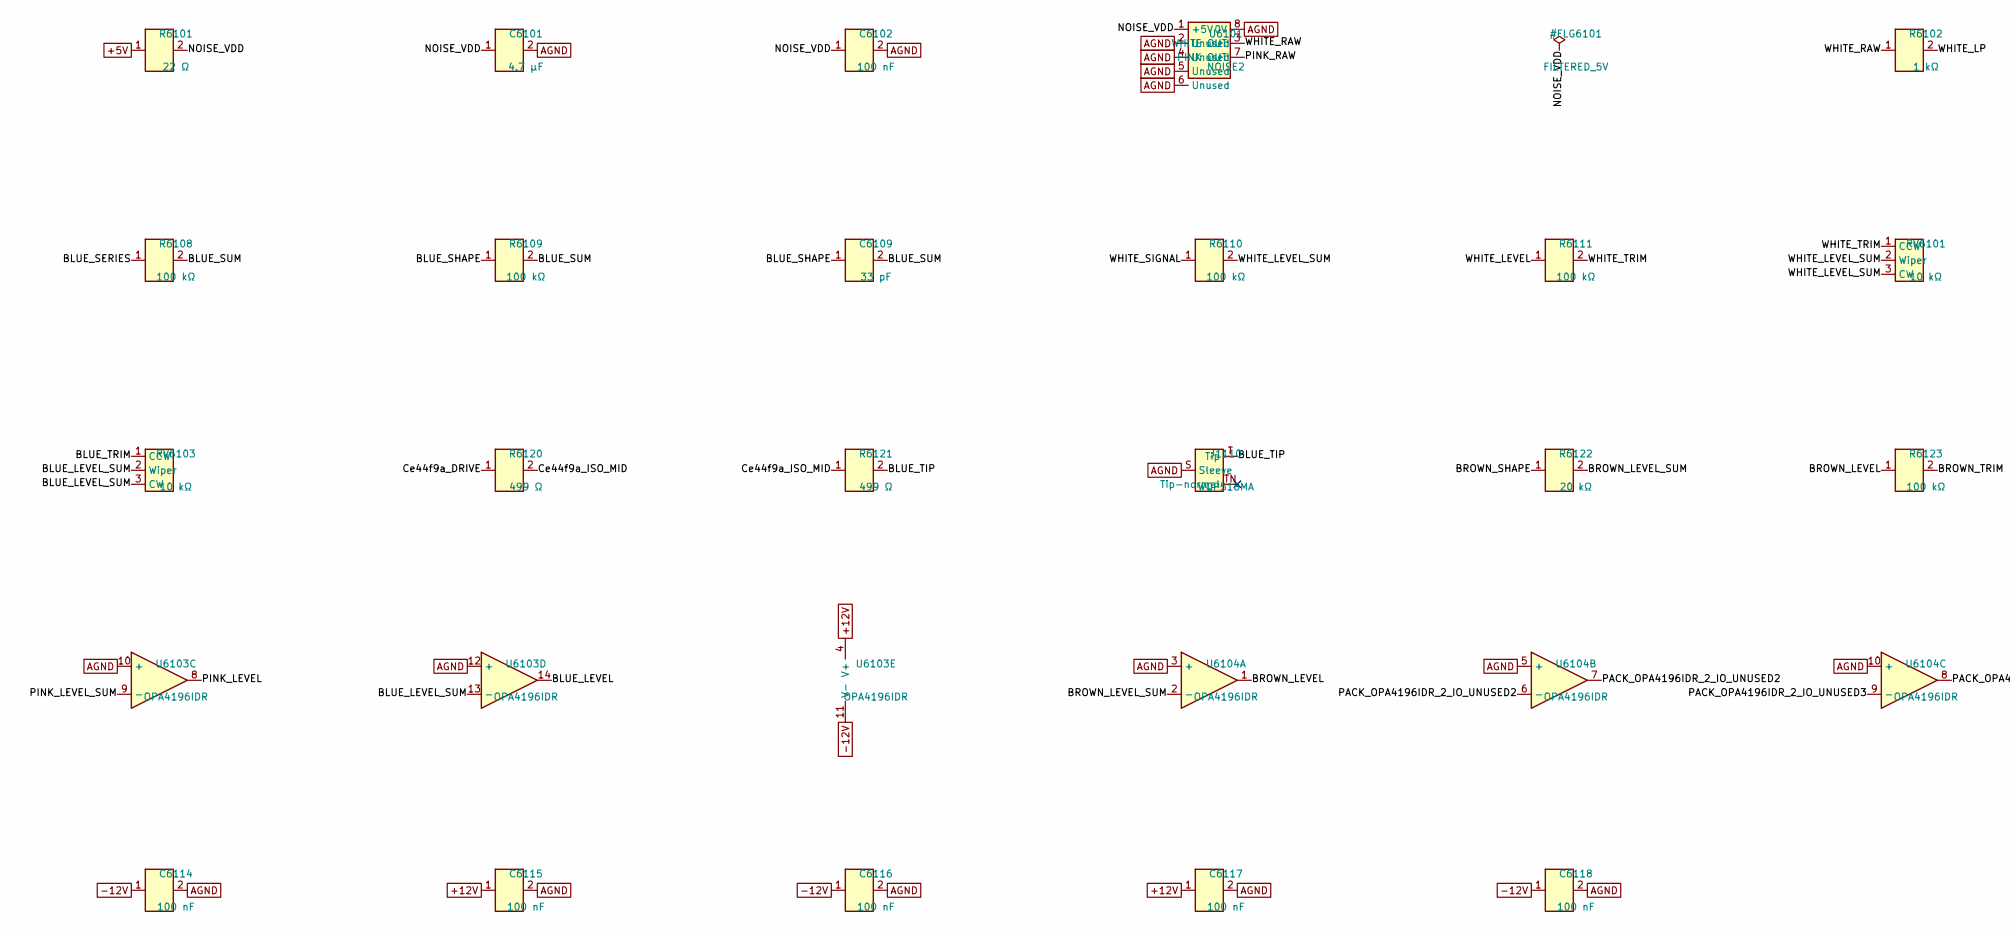
[picture p135: schematic noise.kicad_sch, part in row 1, column 1]

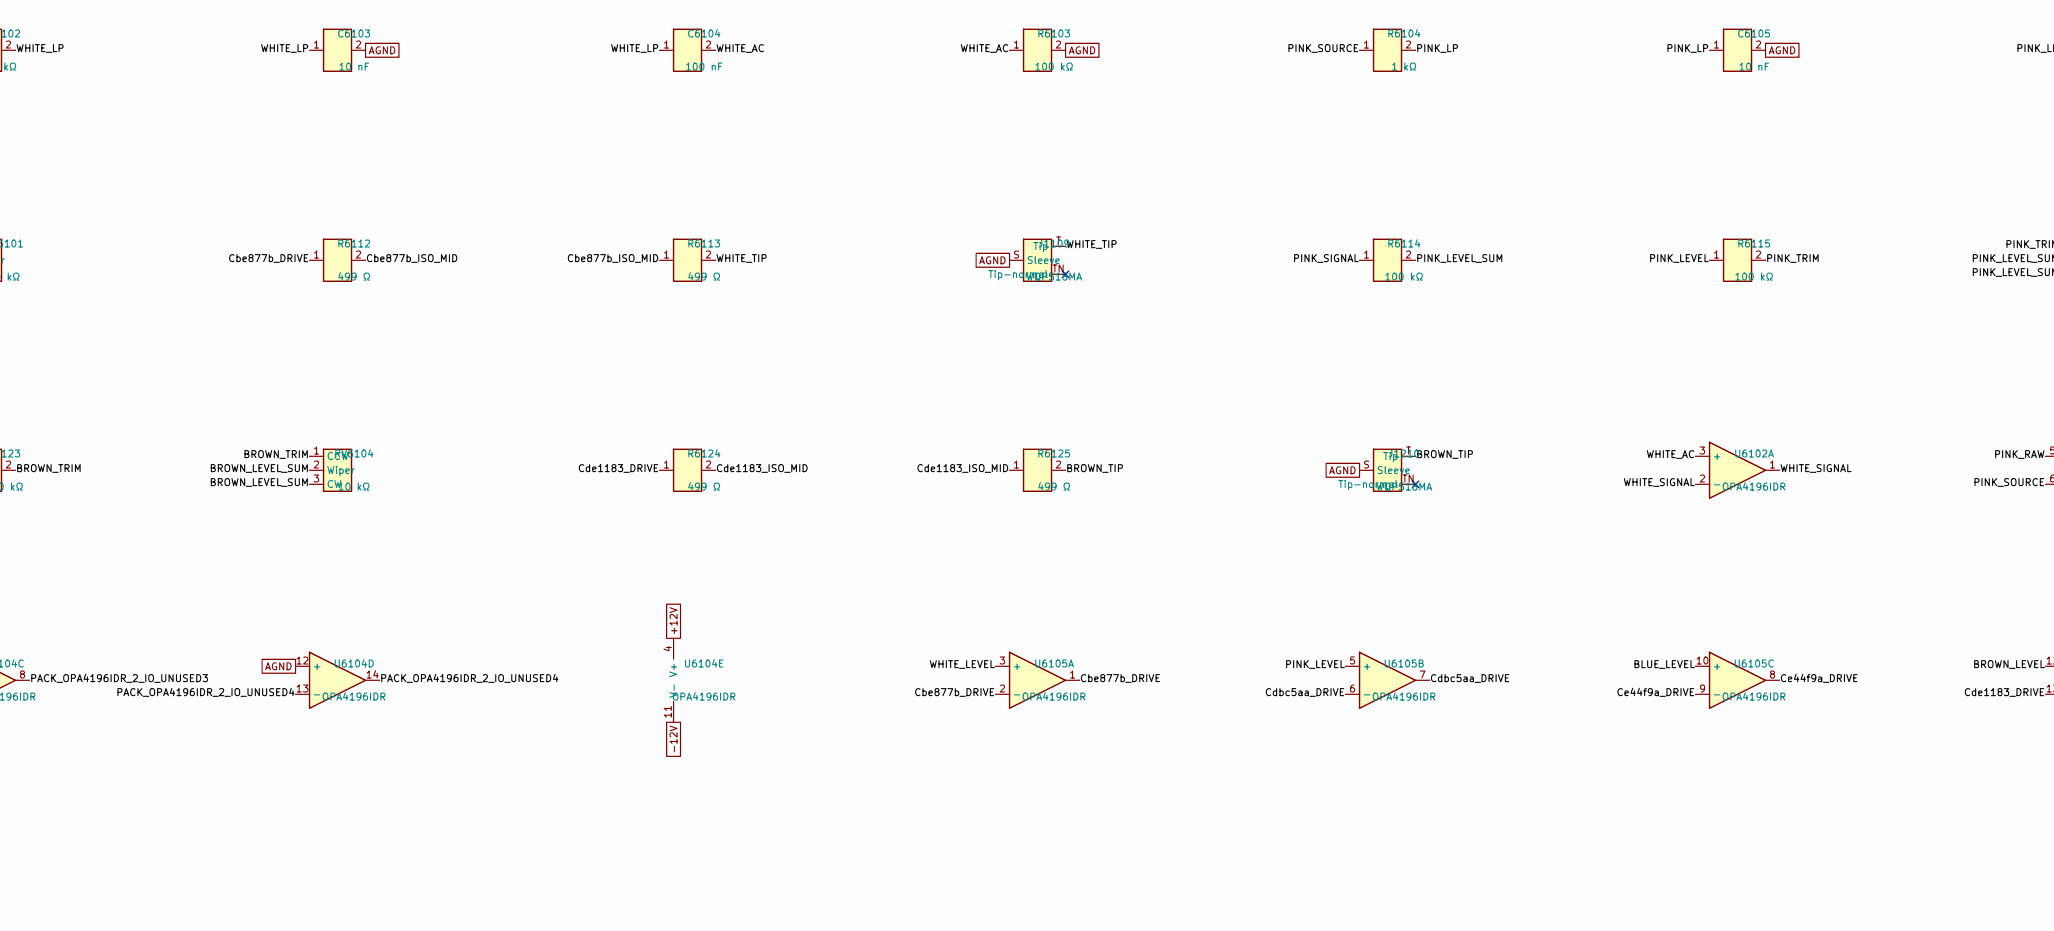
[picture p136: schematic noise.kicad_sch, part in row 1, column 2]

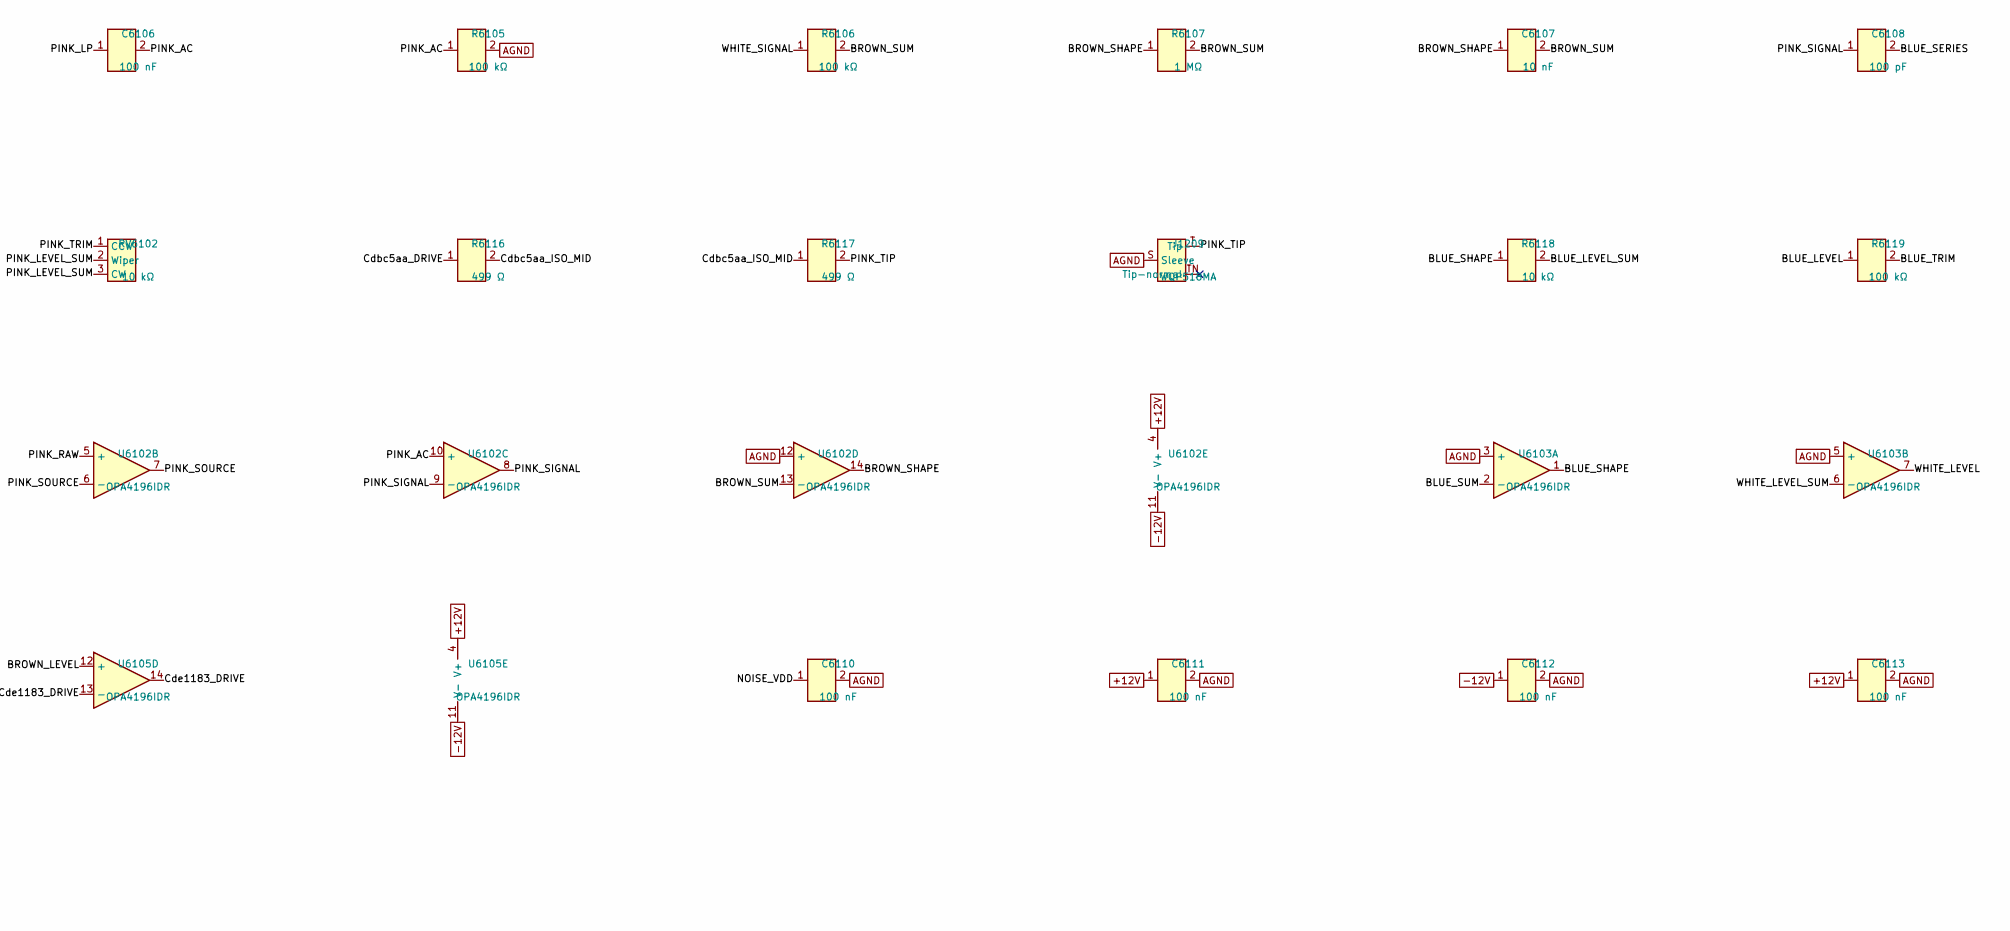
[picture p137: schematic noise.kicad_sch, part in row 1, column 3]

Parts:
C6101: 4.7 µF; C0603
C6102, C6104, C6106, C6110, C6111, C6112, C6113, C6114, C6115, C6116, C6117, C6118: 100 nF; C0603; MPN GRM188R71H104KA93D
C6103, C6105, C6107: 10 nF; C0603
C6108: 100 pF; C0603; MPN C0603C101J5GACTU
C6109: 33 pF; C0603
J1109, J1110, J1209, J1210: WQP518MA; Jack_3.5mm_QingPu_WQP518MA; MPN WQP518MA
R6101: 22 Ω; R0603
R6102, R6104: 1 kΩ; R0603
R6103, R6105, R6106, R6108, R6109, R6110, R6111, R6114, R6115, R6119, R6123: 100 kΩ; R0603; MPN RT0603BRD07100KL
R6107: 1 MΩ; R0603
R6112, R6113, R6116, R6117, R6120, R6121, R6124, R6125: 499 Ω; R_1210_3225Metric; MPN RC1210FR-07499RL
R6118: 10 kΩ; R0603
R6122: 20 kΩ; R0603
RV6101, RV6102, RV6103, RV6104: 10 kΩ; Potentiometer_Bourns_TC33X_Vertical; MPN TC33X-2-103E
U6101: NOISE2; DIP-8_W7.62mm; MPN NOISE2
U6102, U6103, U6104, U6105: OPA4196IDR; SOIC-14_3.9x8.7mm_P1.27mm; MPN OPA4196IDR; LCSC C2057385

Connections:
+5V: R6101.1
+12V: C6111.1, C6113.1, C6115.1, C6117.1, U6102.4 (V+), U6103.4 (V+), U6104.4 (V+), U6105.4 (V+)
-12V: C6112.1, C6114.1, C6116.1, C6118.1, U6102.11 (V-), U6103.11 (V-), U6104.11 (V-), U6105.11 (V-)
AGND: C6101.2, C6102.2, C6103.2, C6105.2, C6110.2, C6111.2, C6112.2, C6113.2, C6114.2, C6115.2, C6116.2, C6117.2, C6118.2, J1109.S (Sleeve), J1110.S (Sleeve), J1209.S (Sleeve), J1210.S (Sleeve), R6103.2, R6105.2, U6101.2 (Unused), U6101.4 (Unused), U6101.5 (Unused), U6101.6 (Unused), U6101.8 (0V), U6102.12 (+), U6103.3 (+), U6103.5 (+), U6103.10 (+), U6103.12 (+), U6104.3 (+), U6104.5 (+), U6104.10 (+), U6104.12 (+)
BLUE_LEVEL: R6119.1, U6103.14, U6105.10 (+)
BLUE_LEVEL_SUM: R6118.2, RV6103.2 (Wiper), RV6103.3 (CW), U6103.13 (-)
BLUE_SERIES: C6108.2, R6108.1
BLUE_SHAPE: C6109.1, R6109.1, R6118.1, U6103.1
BLUE_SUM: C6109.2, R6108.2, R6109.2, U6103.2 (-)
BLUE_TIP: J1110.T (Tip), R6121.2
BLUE_TRIM: R6119.2, RV6103.1 (CCW)
BROWN_LEVEL: R6123.1, U6104.1, U6105.12 (+)
BROWN_LEVEL_SUM: R6122.2, RV6104.2 (Wiper), RV6104.3 (CW), U6104.2 (-)
BROWN_SHAPE: C6107.1, R6107.1, R6122.1, U6102.14
BROWN_SUM: C6107.2, R6106.2, R6107.2, U6102.13 (-)
BROWN_TIP: J1210.T (Tip), R6125.2
BROWN_TRIM: R6123.2, RV6104.1 (CCW)
Cbe877b_DRIVE: R6112.1, U6105.1, U6105.2 (-)
Cbe877b_ISO_MID: R6112.2, R6113.1
Cdbc5aa_DRIVE: R6116.1, U6105.6 (-), U6105.7
Cdbc5aa_ISO_MID: R6116.2, R6117.1
Cde1183_DRIVE: R6124.1, U6105.13 (-), U6105.14
Cde1183_ISO_MID: R6124.2, R6125.1
Ce44f9a_DRIVE: R6120.1, U6105.8, U6105.9 (-)
Ce44f9a_ISO_MID: R6120.2, R6121.1
NOISE_VDD: C6101.1, C6102.1, C6110.1, R6101.2, U6101.1 (+5V)
PACK_OPA4196IDR_2_IO_UNUSED2: U6104.6 (-), U6104.7
PACK_OPA4196IDR_2_IO_UNUSED3: U6104.8, U6104.9 (-)
PACK_OPA4196IDR_2_IO_UNUSED4: U6104.13 (-), U6104.14
PINK_AC: C6106.2, R6105.1, U6102.10 (+)
PINK_LEVEL: R6115.1, U6103.8, U6105.5 (+)
PINK_LEVEL_SUM: R6114.2, RV6102.2 (Wiper), RV6102.3 (CW), U6103.9 (-)
PINK_LP: C6105.1, C6106.1, R6104.2
PINK_RAW: U6101.7 (PINK OUT), U6102.5 (+)
PINK_SIGNAL: C6108.1, R6114.1, U6102.8, U6102.9 (-)
PINK_SOURCE: R6104.1, U6102.6 (-), U6102.7
PINK_TIP: J1209.T (Tip), R6117.2
PINK_TRIM: R6115.2, RV6102.1 (CCW)
WHITE_AC: C6104.2, R6103.1, U6102.3 (+)
WHITE_LEVEL: R6111.1, U6103.7, U6105.3 (+)
WHITE_LEVEL_SUM: R6110.2, RV6101.2 (Wiper), RV6101.3 (CW), U6103.6 (-)
WHITE_LP: C6103.1, C6104.1, R6102.2
WHITE_RAW: R6102.1, U6101.3 (WHITE OUT)
WHITE_SIGNAL: R6106.1, R6110.1, U6102.1, U6102.2 (-)
WHITE_TIP: J1109.T (Tip), R6113.2
WHITE_TRIM: R6111.2, RV6101.1 (CCW)
