Takazudo/zudo-osc-hole-field/schematic/sheets/octave_reference.kicad_sch

## KiCad design schematic/sheets/octave_reference.kicad_sch (2026-09-30)

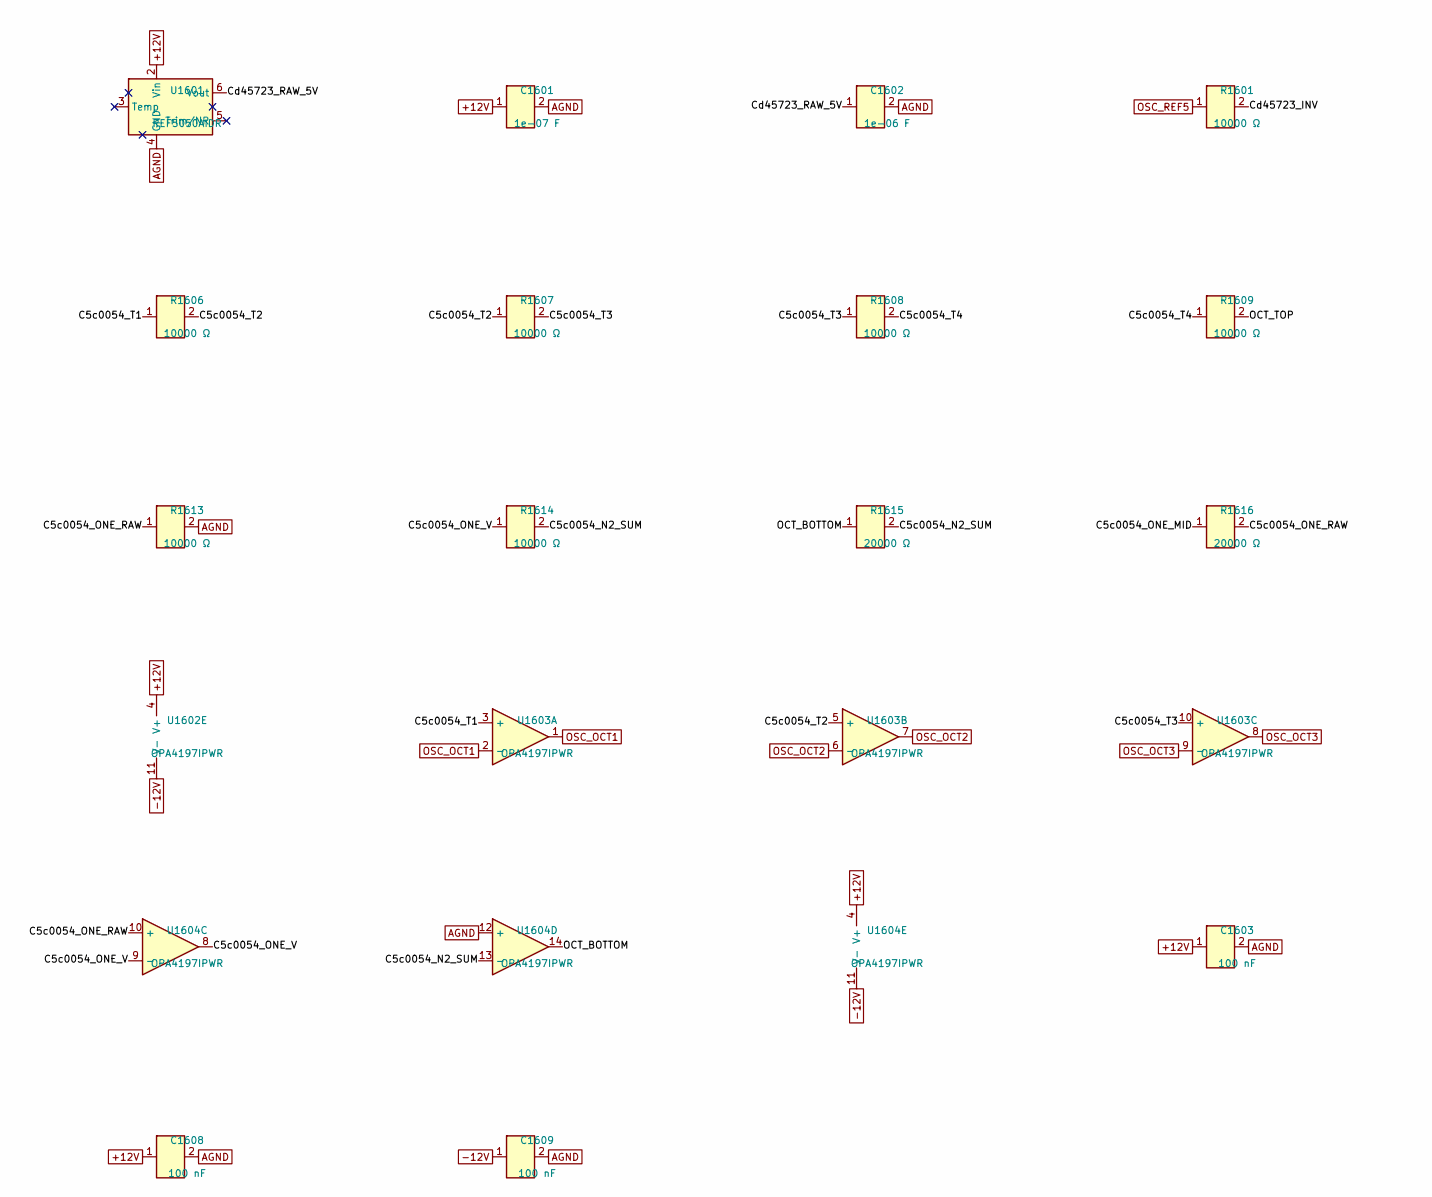
[picture p138: schematic octave_reference.kicad_sch, part in row 1, column 1]

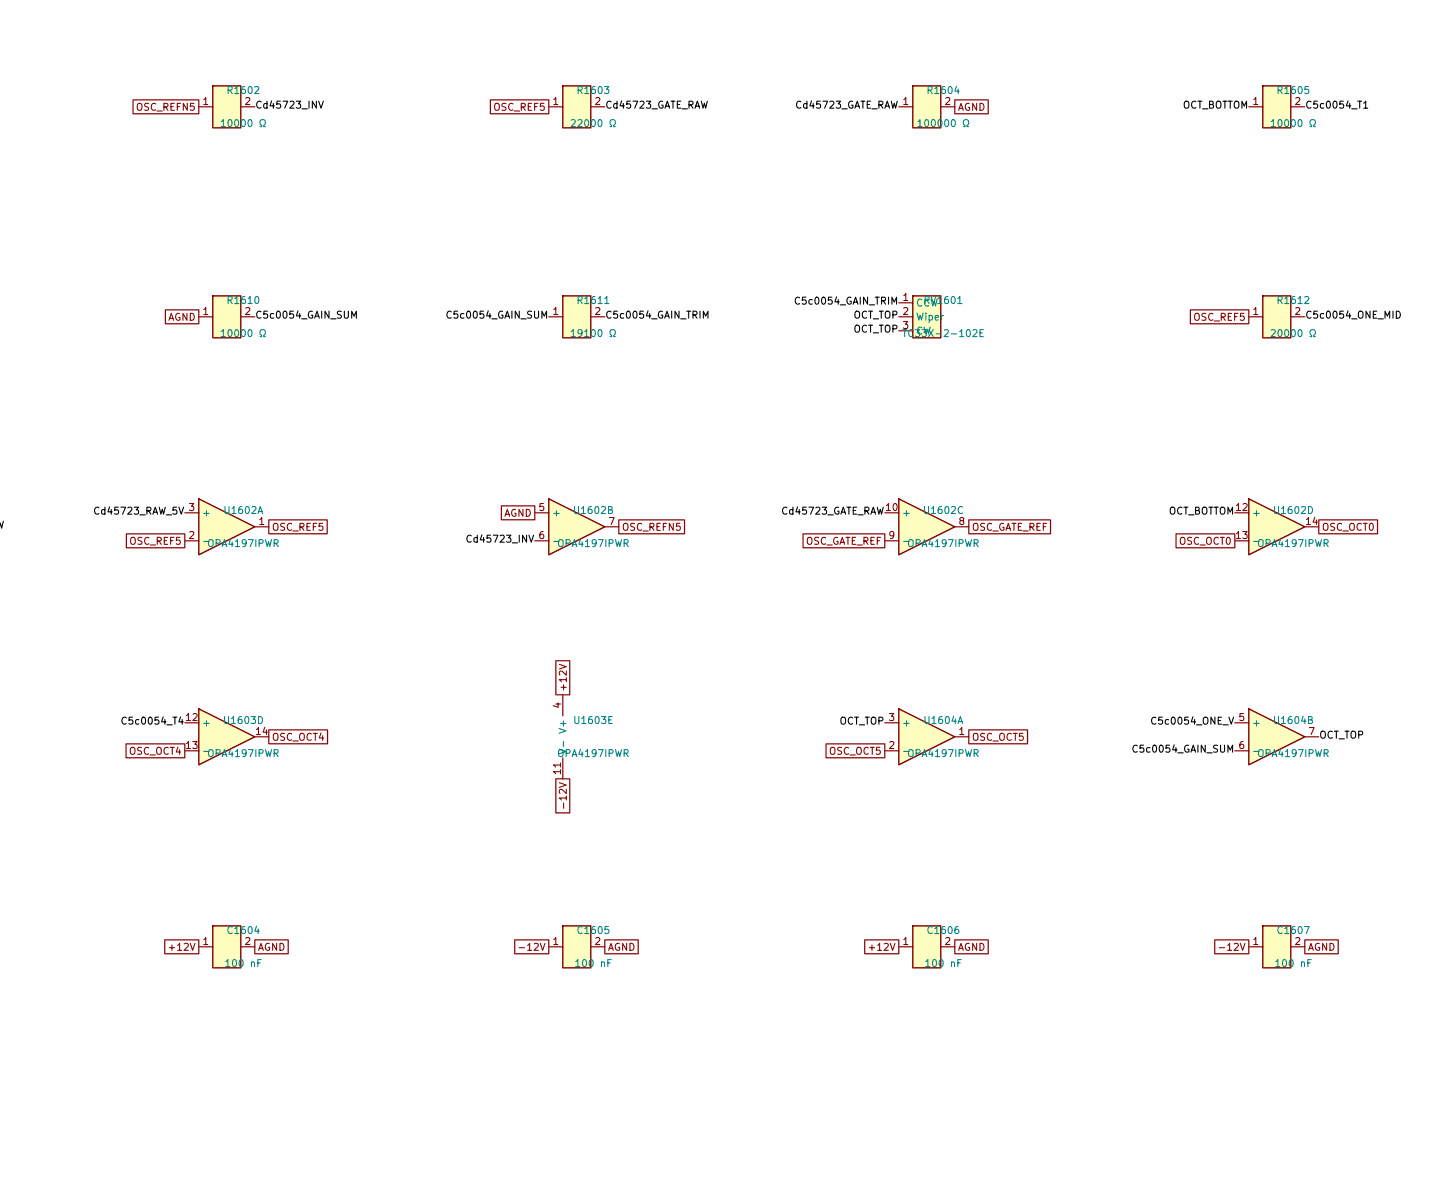
[picture p139: schematic octave_reference.kicad_sch, part in row 1, column 2]

Parts:
C1601: 1e-07 F; C0603; MPN GRM188R71H104KA93D
C1602: 1e-06 F; C0603
C1603, C1604, C1605, C1606, C1607, C1608, C1609: 100 nF; C0603; MPN GRM188R71H104KA93D
R1601, R1602, R1605, R1606, R1607, R1608, R1609, R1610, R1613, R1614: 10000 Ω; R0603
R1603: 22000 Ω; R0603
R1604: 100000 Ω; R0603; MPN RT0603BRD07100KL
R1611: 19100 Ω; R0603
R1612, R1615, R1616: 20000 Ω; R0603
RV1601: TC33X-2-102E; Potentiometer_Bourns_TC33X_Vertical; MPN TC33X-2-102E
U1601: REF5050AIDR; SOIC-8_3.9x4.9mm_P1.27mm; MPN REF5050AIDR; LCSC C27804
U1602, U1603, U1604: OPA4197IPWR; TSSOP-14_4.4x5mm_P0.65mm; MPN OPA4197IPWR; LCSC C2057327

Connections:
+12V: C1601.1, C1603.1, C1604.1, C1606.1, C1608.1, U1601.2 (Vin), U1602.4 (V+), U1603.4 (V+), U1604.4 (V+)
-12V: C1605.1, C1607.1, C1609.1, U1602.11 (V-), U1603.11 (V-), U1604.11 (V-)
AGND: C1601.2, C1602.2, C1603.2, C1604.2, C1605.2, C1606.2, C1607.2, C1608.2, C1609.2, R1604.2, R1610.1, R1613.2, U1601.4 (GND), U1602.5 (+), U1604.12 (+)
C5c0054_GAIN_SUM: R1610.2, R1611.1, U1604.6 (-)
C5c0054_GAIN_TRIM: R1611.2, RV1601.1 (CCW)
C5c0054_N2_SUM: R1614.2, R1615.2, U1604.13 (-)
C5c0054_ONE_MID: R1612.2, R1616.1
C5c0054_ONE_RAW: R1613.1, R1616.2, U1604.10 (+)
C5c0054_ONE_V: R1614.1, U1604.5 (+), U1604.8, U1604.9 (-)
C5c0054_T1: R1605.2, R1606.1, U1603.3 (+)
C5c0054_T2: R1606.2, R1607.1, U1603.5 (+)
C5c0054_T3: R1607.2, R1608.1, U1603.10 (+)
C5c0054_T4: R1608.2, R1609.1, U1603.12 (+)
Cd45723_GATE_RAW: R1603.2, R1604.1, U1602.10 (+)
Cd45723_INV: R1601.2, R1602.2, U1602.6 (-)
Cd45723_RAW_5V: C1602.1, U1601.6 (Vout), U1602.3 (+)
OCT_BOTTOM: R1605.1, R1615.1, U1602.12 (+), U1604.14
OCT_TOP: R1609.2, RV1601.2 (Wiper), RV1601.3 (CW), U1604.3 (+), U1604.7
OSC_GATE_REF: U1602.8, U1602.9 (-)
OSC_OCT0: U1602.13 (-), U1602.14
OSC_OCT1: U1603.1, U1603.2 (-)
OSC_OCT2: U1603.6 (-), U1603.7
OSC_OCT3: U1603.8, U1603.9 (-)
OSC_OCT4: U1603.13 (-), U1603.14
OSC_OCT5: U1604.1, U1604.2 (-)
OSC_REF5: R1601.1, R1603.1, R1612.1, U1602.1, U1602.2 (-)
OSC_REFN5: R1602.1, U1602.7
