Takazudo/zudo-osc-hole-field/schematic/sheets/offset.kicad_sch

## KiCad design schematic/sheets/offset.kicad_sch (2026-10-02)

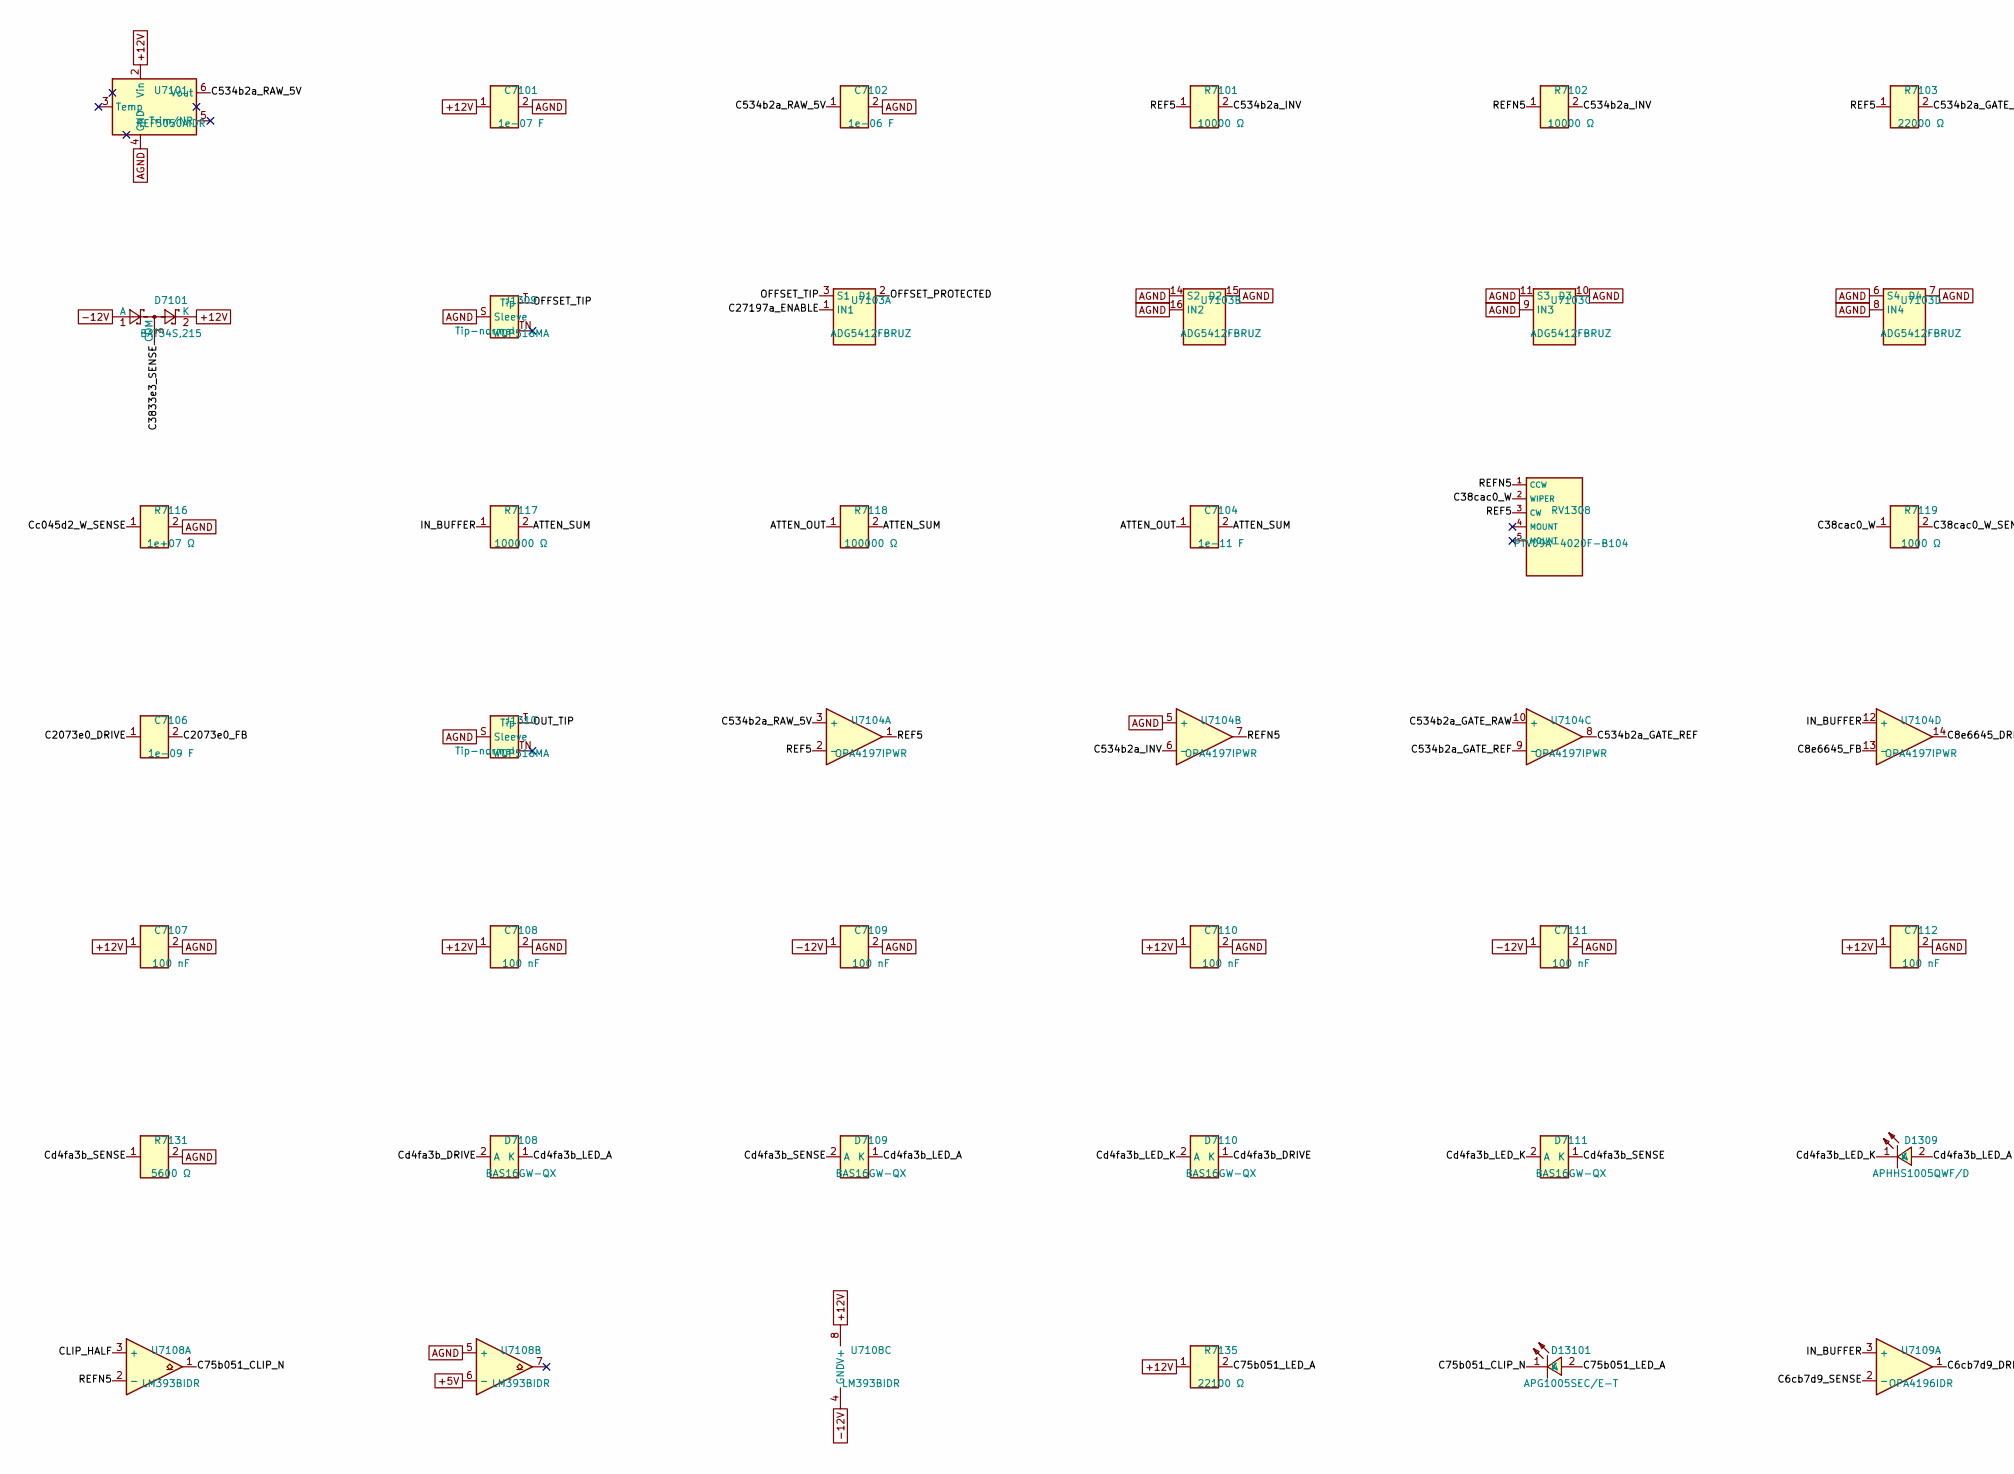
[picture p140: schematic offset.kicad_sch, part in row 1, column 1]

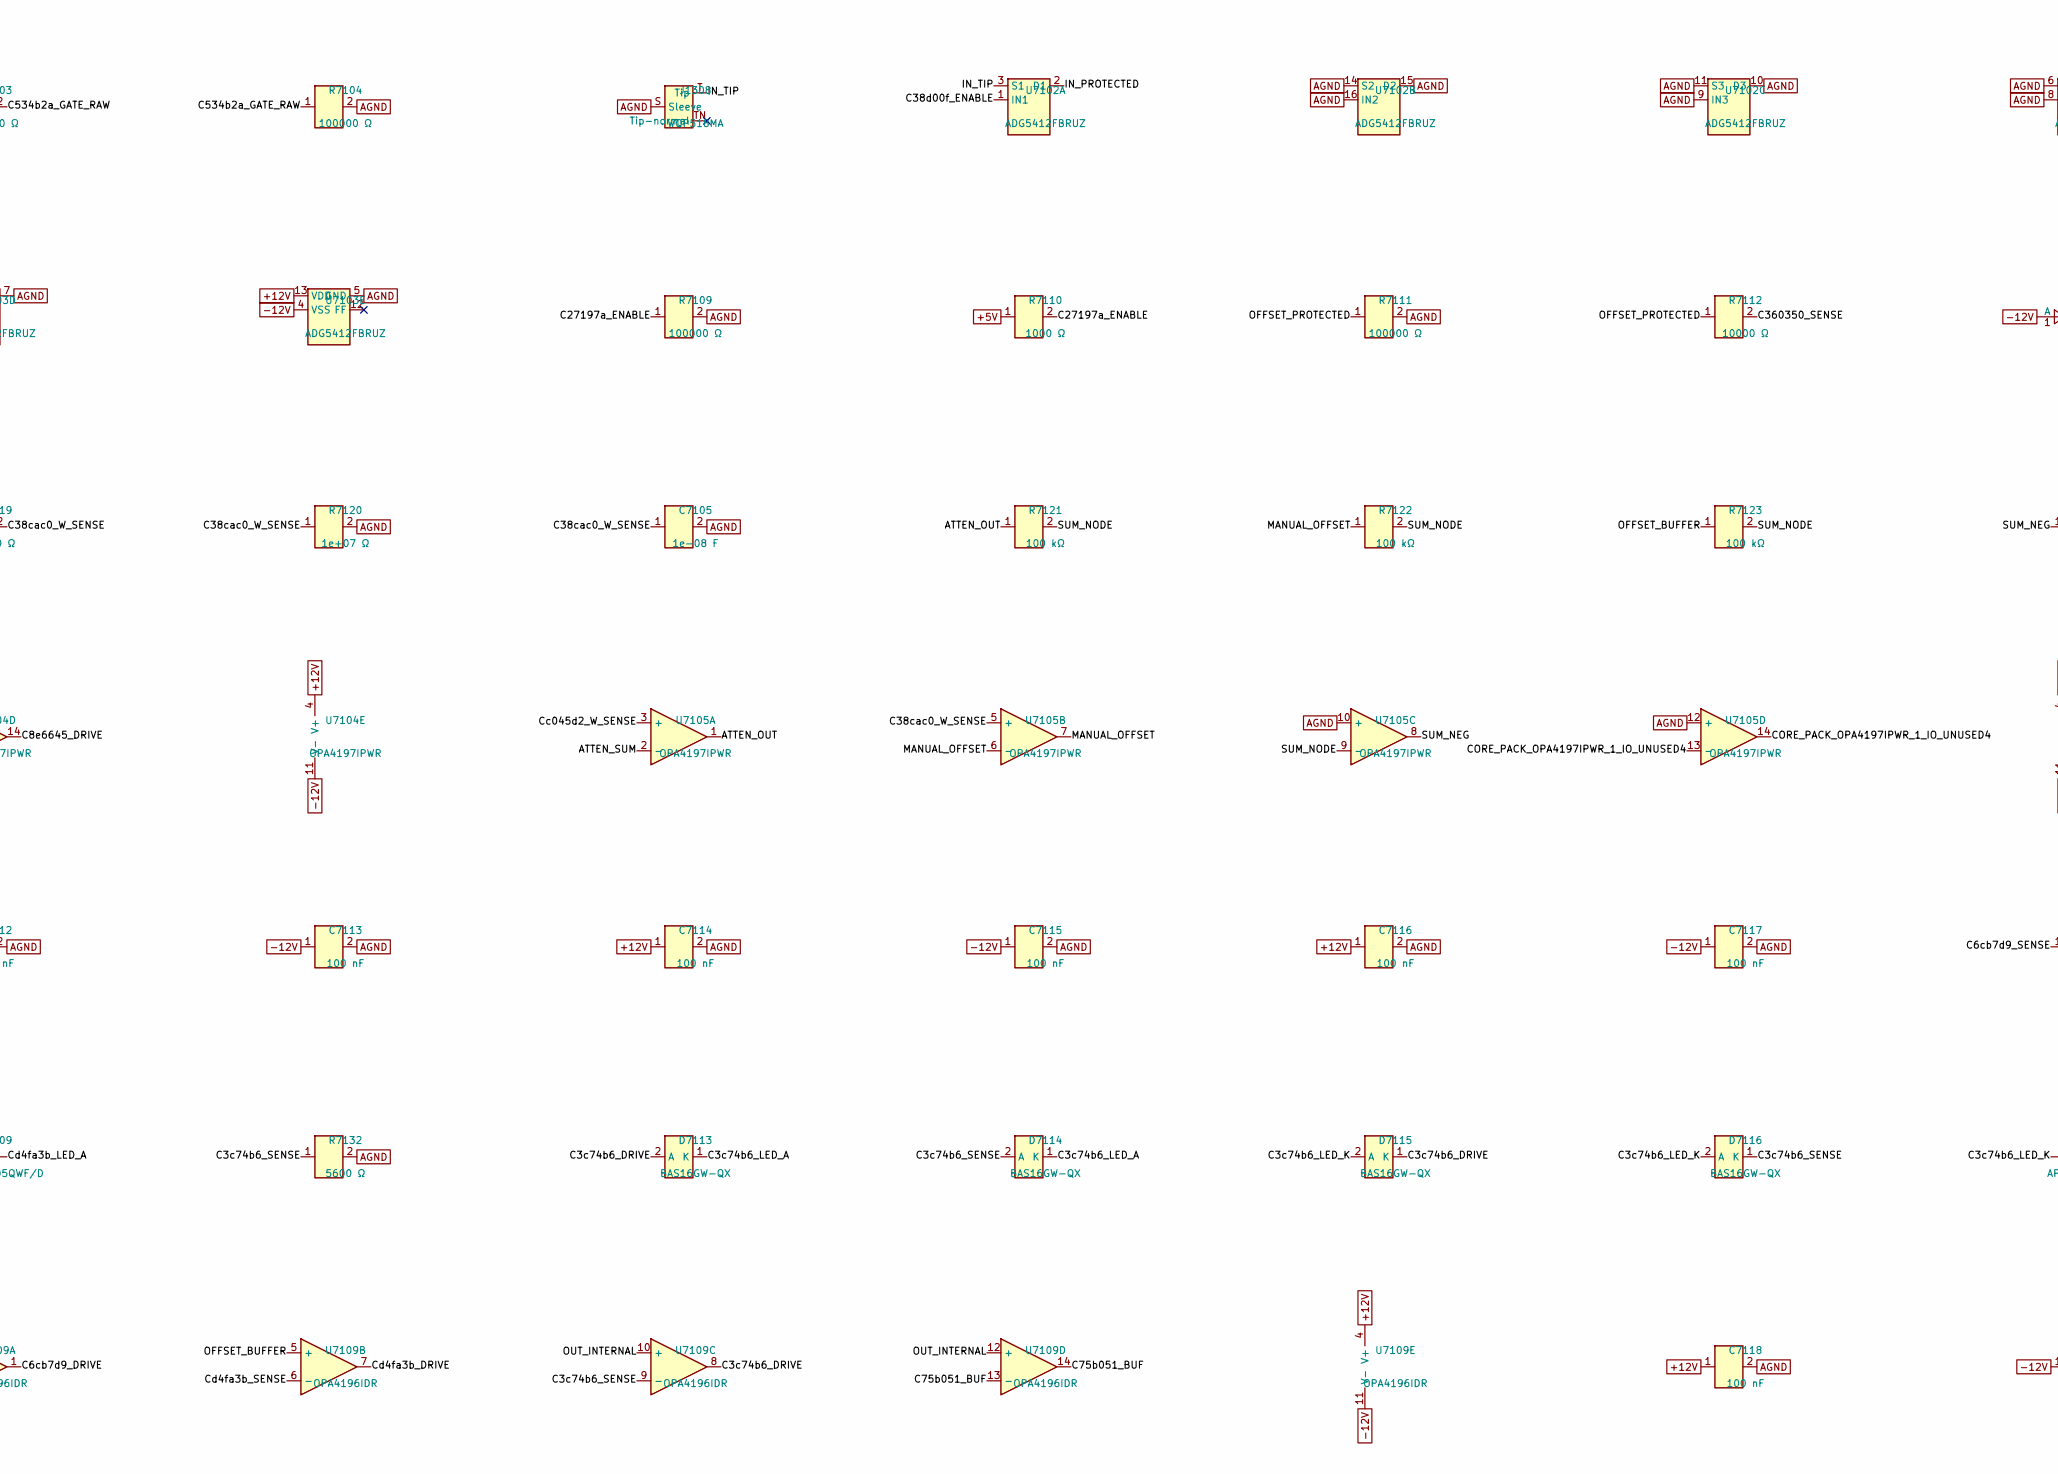
[picture p141: schematic offset.kicad_sch, part in row 1, column 2]

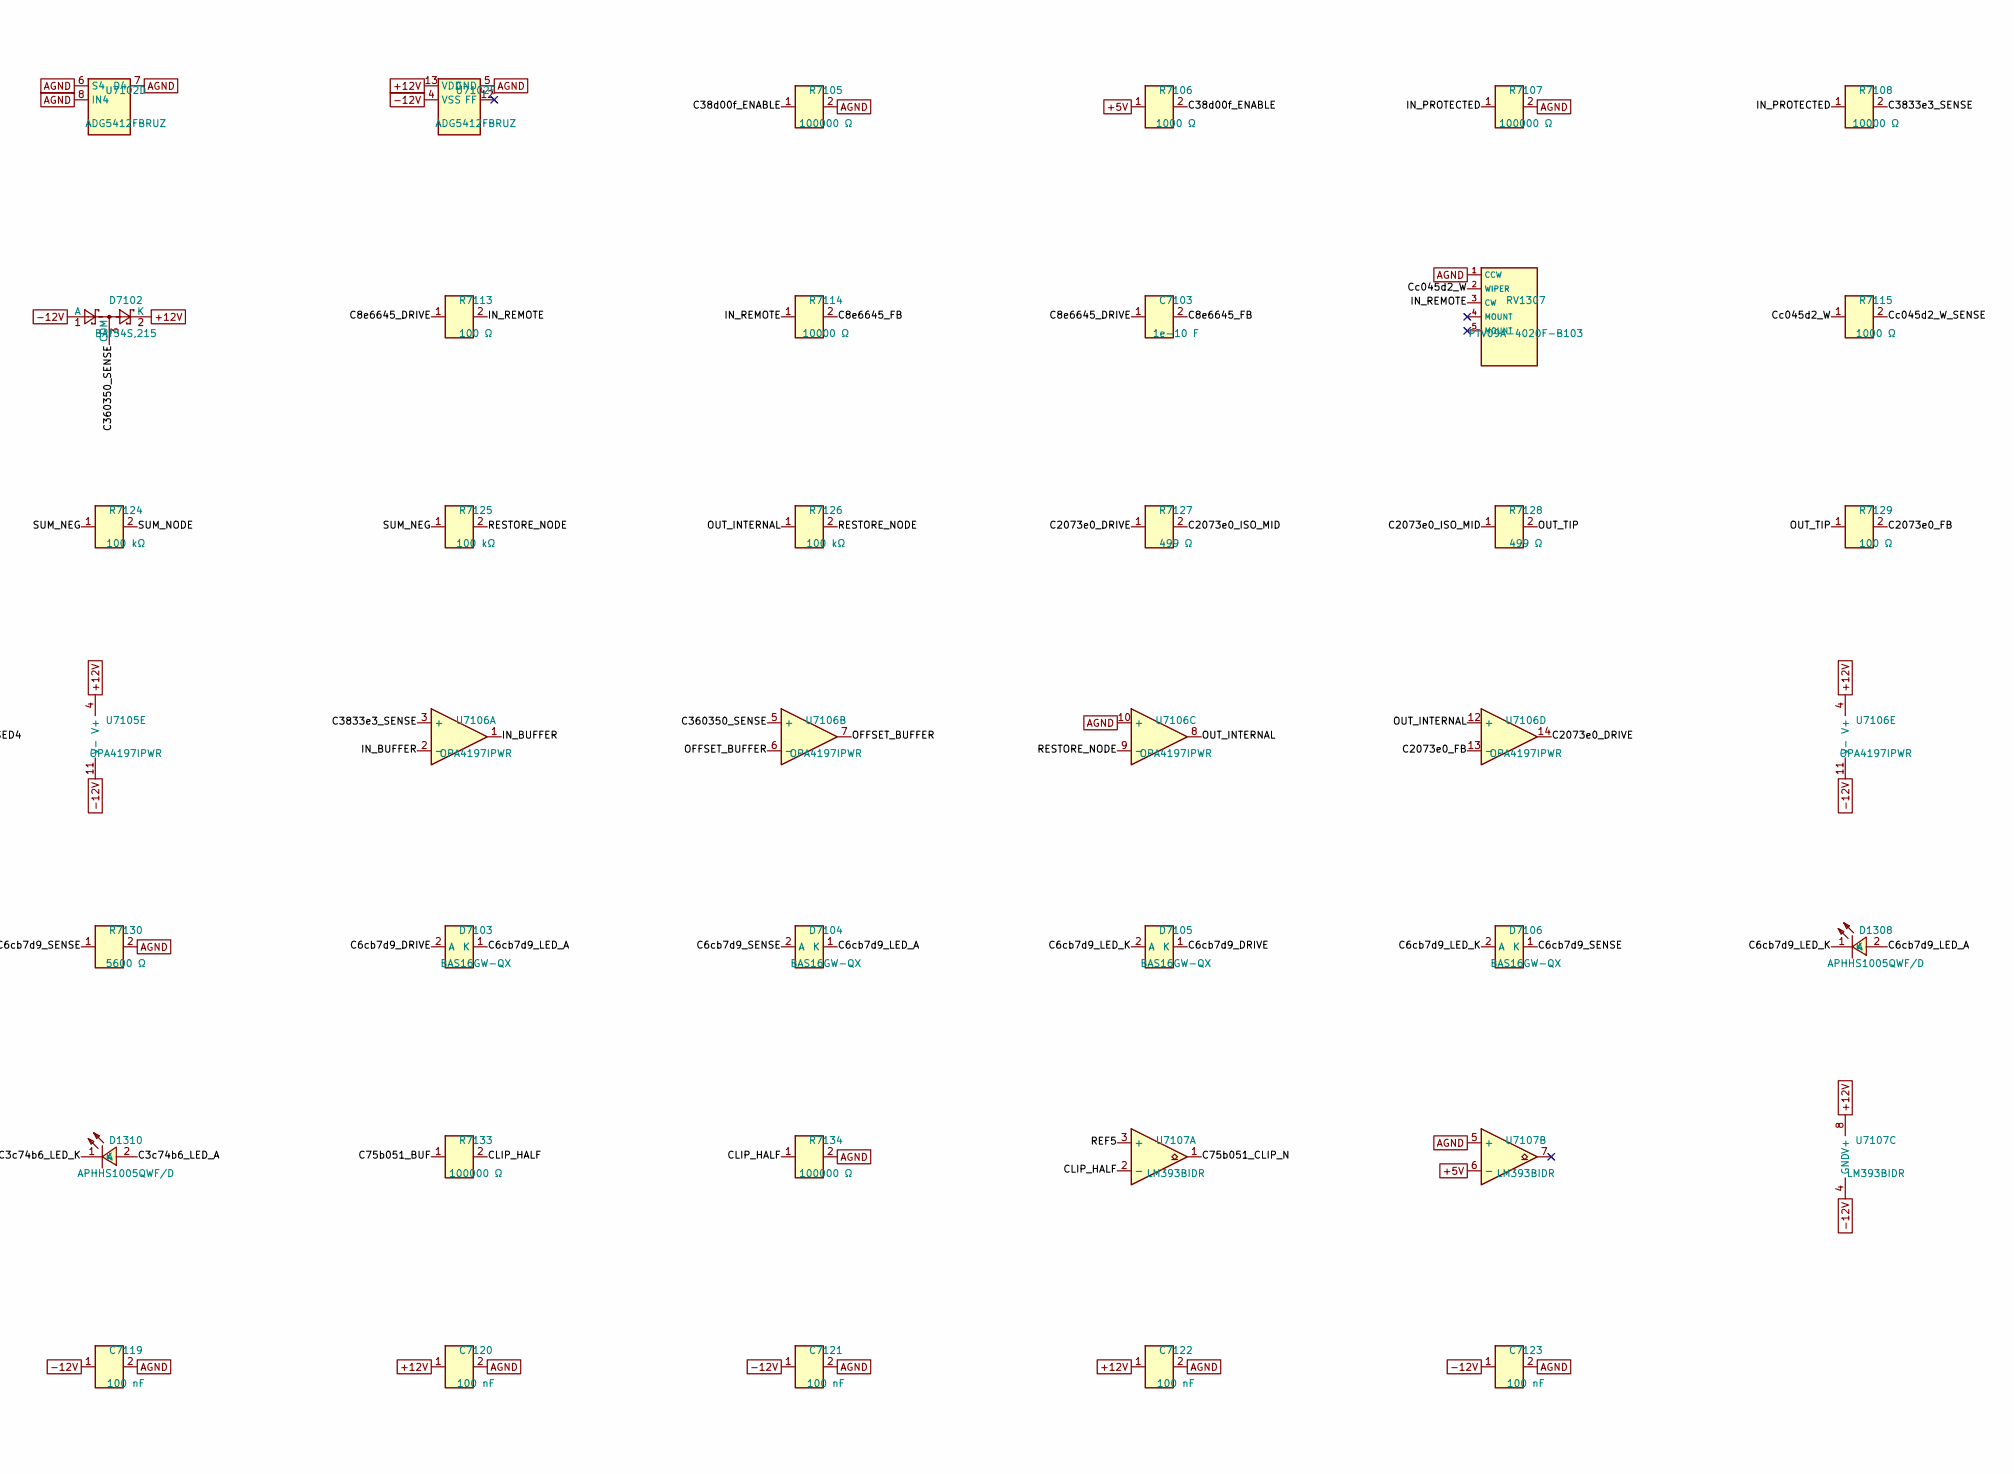
[picture p142: schematic offset.kicad_sch, part in row 1, column 3]

Parts:
C7101: 1e-07 F; C0603; MPN GRM188R71H104KA93D
C7102: 1e-06 F; C0603
C7103: 1e-10 F; C0603; MPN C0603C101J5GACTU
C7104: 1e-11 F; C0603
C7105: 1e-08 F; C0603
C7106: 1e-09 F; C0603; MPN C0603C102J5GACTU
C7107, C7108, C7109, C7110, C7111, C7112, C7113, C7114, C7115, C7116, C7117, C7118, C7119, C7120, C7121, C7122, C7123: 100 nF; C0603; MPN GRM188R71H104KA93D
D1308, D1309, D1310: APHHS1005QWF/D; LED0402-Kingbright-White; MPN APHHS1005QWF/D
D7101, D7102: BAT54S,215; SOT-23; MPN BAT54S,215
D7103, D7104, D7105, D7106, D7108, D7109, D7110, D7111, D7113, D7114, D7115, D7116: BAS16GW-QX; SOD-123; MPN BAS16GW-QX
D13101: APG1005SEC/E-T; LED0402-Kingbright-Red; MPN APG1005SEC/E-T
J1308, J1309, J1310: WQP518MA; Jack_3.5mm_QingPu_WQP518MA; MPN WQP518MA
R7101, R7102, R7108, R7112, R7114: 10000 Ω; R0603
R7103: 22000 Ω; R0603
R7104, R7117, R7118, R7133, R7134: 100000 Ω; R0603; MPN RT0603BRD07100KL
R7105, R7107, R7109, R7111: 100000 Ω; R0603; MPN RC0603FR-07100KL
R7106, R7110, R7115, R7119: 1000 Ω; R0603
R7113: 100 Ω; R0603
R7116, R7120: 1e+07 Ω; R0603
R7121, R7122, R7123, R7124, R7125, R7126: 100 kΩ; R0603; MPN RT0603BRD07100KL
R7127, R7128: 499 Ω; R_1210_3225Metric; MPN RC1210FR-07499RL
R7129: 100 Ω; R0603; MPN RC0603FR-07100RL
R7130, R7131, R7132: 5600 Ω; R0603
R7135: 22100 Ω; R0603
RV1307: PTV09A-4020F-B103; PTV09A-4020F; MPN PTV09A-4020F-B103; LCSC C5848782
RV1308: PTV09A-4020F-B104; PTV09A-4020F; MPN PTV09A-4020F-B104
U7101: REF5050AIDR; SOIC-8_3.9x4.9mm_P1.27mm; MPN REF5050AIDR; LCSC C27804
U7102, U7103: ADG5412FBRUZ; TSSOP-16_4.4x5mm_P0.65mm; MPN ADG5412FBRUZ; LCSC C579073
U7104, U7105, U7106: OPA4197IPWR; TSSOP-14_4.4x5mm_P0.65mm; MPN OPA4197IPWR; LCSC C2057327
U7107, U7108: LM393BIDR; SOIC-8_3.9x4.9mm_P1.27mm; MPN LM393BIDR
U7109: OPA4196IDR; SOIC-14_3.9x8.7mm_P1.27mm; MPN OPA4196IDR; LCSC C2057385

Connections:
+5V: R7106.1, R7110.1, U7107.6 (-), U7108.6 (-)
+12V: C7101.1, C7107.1, C7108.1, C7110.1, C7112.1, C7114.1, C7116.1, C7118.1, C7120.1, C7122.1, D7101.2 (K), D7102.2 (K), R7135.1, U7101.2 (Vin), U7102.13 (VDD), U7103.13 (VDD), U7104.4 (V+), U7105.4 (V+), U7106.4 (V+), U7107.8 (V+), U7108.8 (V+), U7109.4 (V+)
-12V: C7109.1, C7111.1, C7113.1, C7115.1, C7117.1, C7119.1, C7121.1, C7123.1, D7101.1 (A), D7102.1 (A), U7102.4 (VSS), U7103.4 (VSS), U7104.11 (V-), U7105.11 (V-), U7106.11 (V-), U7107.4 (GND), U7108.4 (GND), U7109.11 (V-)
AGND: C7101.2, C7102.2, C7105.2, C7107.2, C7108.2, C7109.2, C7110.2, C7111.2, C7112.2, C7113.2, C7114.2, C7115.2, C7116.2, C7117.2, C7118.2, C7119.2, C7120.2, C7121.2, C7122.2, C7123.2, J1308.S (Sleeve), J1309.S (Sleeve), J1310.S (Sleeve), R7104.2, R7105.2, R7107.2, R7109.2, R7111.2, R7116.2, R7120.2, R7130.2, R7131.2, R7132.2, R7134.2, RV1307.1 (CCW), U7101.4 (GND), U7102.5 (GND), U7102.6 (S4), U7102.7 (D4), U7102.8 (IN4), U7102.9 (IN3), U7102.10 (D3), U7102.11 (S3), U7102.14 (S2), U7102.15 (D2), U7102.16 (IN2), U7103.5 (GND), U7103.6 (S4), U7103.7 (D4), U7103.8 (IN4), U7103.9 (IN3), U7103.10 (D3), U7103.11 (S3), U7103.14 (S2), U7103.15 (D2), U7103.16 (IN2), U7104.5 (+), U7105.10 (+), U7105.12 (+), U7106.10 (+), U7107.5 (+), U7108.5 (+)
ATTEN_OUT: C7104.1, R7118.1, R7121.1, U7105.1
ATTEN_SUM: C7104.2, R7117.2, R7118.2, U7105.2 (-)
C3c74b6_DRIVE: D7113.2 (A), D7115.1 (K), U7109.8
C3c74b6_LED_A: D1310.2 (A), D7113.1 (K), D7114.1 (K)
C3c74b6_LED_K: D1310.1 (K), D7115.2 (A), D7116.2 (A)
C3c74b6_SENSE: D7114.2 (A), D7116.1 (K), R7132.1, U7109.9 (-)
C6cb7d9_DRIVE: D7103.2 (A), D7105.1 (K), U7109.1
C6cb7d9_LED_A: D1308.2 (A), D7103.1 (K), D7104.1 (K)
C6cb7d9_LED_K: D1308.1 (K), D7105.2 (A), D7106.2 (A)
C6cb7d9_SENSE: D7104.2 (A), D7106.1 (K), R7130.1, U7109.2 (-)
C8e6645_DRIVE: C7103.1, R7113.1, U7104.14
C8e6645_FB: C7103.2, R7114.2, U7104.13 (-)
C38cac0_W: R7119.1, RV1308.2 (WIPER)
C38cac0_W_SENSE: C7105.1, R7119.2, R7120.1, U7105.5 (+)
C38d00f_ENABLE: R7105.1, R7106.2, U7102.1 (IN1)
C75b051_BUF: R7133.1, U7109.13 (-), U7109.14
C75b051_CLIP_N: D13101.1 (K), U7107.1, U7108.1
C75b051_LED_A: D13101.2 (A), R7135.2
C534b2a_GATE_RAW: R7103.2, R7104.1, U7104.10 (+)
C534b2a_GATE_REF: U7104.8, U7104.9 (-)
C534b2a_INV: R7101.2, R7102.2, U7104.6 (-)
C534b2a_RAW_5V: C7102.1, U7101.6 (Vout), U7104.3 (+)
C2073e0_DRIVE: C7106.1, R7127.1, U7106.14
C2073e0_FB: C7106.2, R7129.2, U7106.13 (-)
C2073e0_ISO_MID: R7127.2, R7128.1
C3833e3_SENSE: D7101.3 (COM), R7108.2, U7106.3 (+)
C27197a_ENABLE: R7109.1, R7110.2, U7103.1 (IN1)
C360350_SENSE: D7102.3 (COM), R7112.2, U7106.5 (+)
CLIP_HALF: R7133.2, R7134.1, U7107.2 (-), U7108.3 (+)
CORE_PACK_OPA4197IPWR_1_IO_UNUSED4: U7105.13 (-), U7105.14
Cc045d2_W: R7115.1, RV1307.2 (WIPER)
Cc045d2_W_SENSE: R7115.2, R7116.1, U7105.3 (+)
Cd4fa3b_DRIVE: D7108.2 (A), D7110.1 (K), U7109.7
Cd4fa3b_LED_A: D1309.2 (A), D7108.1 (K), D7109.1 (K)
Cd4fa3b_LED_K: D1309.1 (K), D7110.2 (A), D7111.2 (A)
Cd4fa3b_SENSE: D7109.2 (A), D7111.1 (K), R7131.1, U7109.6 (-)
IN_BUFFER: R7117.1, U7104.12 (+), U7106.1, U7106.2 (-), U7109.3 (+)
IN_PROTECTED: R7107.1, R7108.1, U7102.2 (D1)
IN_REMOTE: R7113.2, R7114.1, RV1307.3 (CW)
IN_TIP: J1308.T (Tip), U7102.3 (S1)
MANUAL_OFFSET: R7122.1, U7105.6 (-), U7105.7
OFFSET_BUFFER: R7123.1, U7106.6 (-), U7106.7, U7109.5 (+)
OFFSET_PROTECTED: R7111.1, R7112.1, U7103.2 (D1)
OFFSET_TIP: J1309.T (Tip), U7103.3 (S1)
OUT_INTERNAL: R7126.1, U7106.8, U7106.12 (+), U7109.10 (+), U7109.12 (+)
OUT_TIP: J1310.T (Tip), R7128.2, R7129.1
REF5: R7101.1, R7103.1, RV1308.3 (CW), U7104.1, U7104.2 (-), U7107.3 (+)
REFN5: R7102.1, RV1308.1 (CCW), U7104.7, U7108.2 (-)
RESTORE_NODE: R7125.2, R7126.2, U7106.9 (-)
SUM_NEG: R7124.1, R7125.1, U7105.8
SUM_NODE: R7121.2, R7122.2, R7123.2, R7124.2, U7105.9 (-)
