Takazudo/zudo-osc-hole-field/schematic/sheets/oscillator.kicad_sch

## KiCad design schematic/sheets/oscillator.kicad_sch (2026-09-30)

Schematic: oscillator.kicad_sch

Parts:
C1101, C1103: 1e-10 F; C0603; MPN C0603C101J5GACTU
C1102, C1104: 1e-11 F; C0603
C1105, C1106, C1107: 1e-08 F; C0603
C1108, C1110, C1121, C1122, C1123, C1124, C1125, C1126, C1127, C1128, C1129, C1130, C1131, C1132, C1133, C1134, C1135, C1136, C1137, C1138, C1139, C1140, C1141, C1142, C1143, C1144, C1145, C1146, C1147, C1148, C1149, C1150, C1151, C1152, C1153: 100 nF; C0603; MPN GRM188R71H104KA93D
C1109: 100 pF; C0603; MPN C0603C101J5GACTU
C1111: 1 nF C0G; C0603
C1112: 10 nF; C0603
C1113, C1114, C1115, C1116, C1117, C1118, C1119, C1120: 1 nF; C0603
DO1101, DO1102, DO1103, DO1104, DO1105: BAT54S,215; SOT-23; MPN BAT54S,215
J101, J102, J103, J104, J105, J106, J107, J108: WQP518MA; Jack_3.5mm_QingPu_WQP518MA; MPN WQP518MA
Q1101: BCM847BS,115; SOT-363_SC-70-6; MPN BCM847BS,115
R1101, R1103, R1105, R1107, R1109, R1111, R1113, R1115: 100000 Ω; R0603; MPN RC0603FR-07100KL
R1102, R1106, R1110, R1114, R1119, R1125, R1129, R1131, R1133: 1000 Ω; R0603
R1104, R1108, R1112, R1116, R1118, R1124, R1158: 10000 Ω; R0603
R1117, R1123, R1148: 100 Ω; R0603
R1120, R1126, R1130, R1132, R1134: 1e+07 Ω; R0603
R1121, R1122, R1127, R1128, R1156: 100000 Ω; R0603; MPN RT0603BRD07100KL
R1135, R1190: 1 kΩ; R0603
R1136, R1139: 10 MΩ; R0603
R1137, R1176: 40 kΩ; R0603
R1138, R1140, R1141, R1145, R1161, R1163, R1166, R1169, R1170, R1172, R1175, R1177, R1179, R1181, R1182, R1183, R1184, R1185, R1187, R1188, R1195, R1196, R1197, R1198, R1199: 100 kΩ; R0603; MPN RT0603BRD07100KL
R1142, R1174: 250 kΩ; R0603
R1143: 5 MΩ; R0603
R1144, R1167: 200 kΩ; R0603
R1146: 82.5 kΩ; R0603
R1147, R1191: 1 MΩ; R0603
R1149, R1162, R1164, R1173, R1192, R1193, R1194: 10 kΩ; R0603
R1150: 24 kΩ; R0603
R1151: 5.72 kΩ; R0603
R1152: 1.5 kΩ; R0603
R1153: 1.2 MΩ; R0603
R1154: 470 Ω; R0603
R1155: 51 kΩ; R0603
R1157: 33200 Ω; R0603
R1159: 390000 Ω; R0603
R1160: 4700 Ω; R0603
R1165: 72 kΩ; R0603
R1168: 1.8 MΩ; R0603
R1171: 25 kΩ; R0603
R1178: 125 kΩ; R0603
R1180: 80 kΩ; R0603
R1186: 4.7 kΩ; R0603
R1189: 68 kΩ; R0603
RB1101: 49.9 kΩ; R0603
RB1102, RB1103, RB1104, RB1105, RB1106, RB1107, RB1108, RB1109: 499 Ω; R_1210_3225Metric; MPN RC1210FR-07499RL
RB1110, RB1111, RB1112, RB1113, RB1114, RB1115, RB1116, RB1117, RB1118, RB1119, RB1120, RB1121: 100 Ω; R0603
RV104, RV105, RV107: PTV09A-4020F-B104; PTV09A-4020F; MPN PTV09A-4020F-B104
RV106, RV108: PTV09A-4020F-B103; PTV09A-4020F; MPN PTV09A-4020F-B103; LCSC C5848782
RVO1106, RVO1107, RVO1110, RVO1111: 10 kΩ; Potentiometer_Bourns_TC33X_Vertical; MPN TC33X-2-103E
RVO1108: 1 kΩ; Potentiometer_Bourns_TC33X_Vertical; MPN TC33X-2-102E
RVO1109: 20 kΩ; Potentiometer_Bourns_TC33X_Vertical
SW101: SRBV160803; MPN SRBV160803; LCSC C470374
SW102: 2MS1T1B1M2QES-5; Toggle_Dailywell_2MS_T1B1M2; MPN 2MS1T1B1M2QES-5; LCSC C908280
SW103: 2MS3T1B1M2QES; Toggle_Dailywell_2MS_T1B1M2; MPN 2MS3T1B1M2QES
U1101, U1102, U1103, U1104: ADG5412FBRUZ; TSSOP-16_4.4x5mm_P0.65mm; MPN ADG5412FBRUZ; LCSC C579073
U1105: AS3340D; SOIC-16_3.9x9.9mm_P1.27mm; MPN AS3340D
U1106, U1108: LM393BIDR; SOIC-8_3.9x4.9mm_P1.27mm; MPN LM393BIDR
U1107: SN74HC14DR; SOIC-14_3.9x8.7mm_P1.27mm; MPN SN74HC14DR
U1109, U1110, U1111, U1118: OPA4197IPWR; TSSOP-14_4.4x5mm_P0.65mm; MPN OPA4197IPWR; LCSC C2057327
U1112, U1113, U1114, U1115, U1116, U1117: OPA4196IDR; SOIC-14_3.9x8.7mm_P1.27mm; MPN OPA4196IDR; LCSC C2057385

Connections:
1V_BUFFER: R1140.1, U1118.1, U1118.2 (-)
1V_PROTECTED: R1103.1, R1104.1, U1101.2 (D1)
1V_TIP: J101.T (Tip), U1101.3 (S1)
+5V: C1132.1, R1102.1, R1106.1, R1110.1, R1114.1, R1160.1, R1186.1, U1106.6 (-), U1107.14 (VCC), U1108.6 (-)
+12V: C1121.1, C1123.1, C1125.1, C1127.1, C1129.1, C1131.1, C1133.1, C1134.1, C1136.1, C1138.1, C1140.1, C1142.1, C1144.1, C1146.1, C1148.1, C1150.1, C1152.1, DO1101.2 (K), DO1102.2 (K), DO1103.2 (K), DO1104.2 (K), R1153.1, R1193.1, R1194.1, U1101.13 (VDD), U1102.13 (VDD), U1103.13 (VDD), U1104.13 (VDD), U1105.16 (VCC), U1106.8 (V+), U1108.8 (V+), U1109.4 (V+), U1110.4 (V+), U1111.4 (V+), U1112.4 (V+), U1113.4 (V+), U1114.4 (V+), U1115.4 (V+), U1116.4 (V+), U1117.4 (V+), U1118.4 (V+)
-12V: C1122.1, C1124.1, C1126.1, C1128.1, C1135.1, C1137.1, C1139.1, C1141.1, C1143.1, C1145.1, C1147.1, C1149.1, C1151.1, C1153.1, DO1101.1 (A), DO1102.1 (A), DO1103.1 (A), DO1104.1 (A), R1192.2, U1101.4 (VSS), U1102.4 (VSS), U1103.4 (VSS), U1104.4 (VSS), U1109.11 (V-), U1110.11 (V-), U1111.11 (V-), U1112.11 (V-), U1113.11 (V-), U1114.11 (V-), U1115.11 (V-), U1116.11 (V-), U1117.11 (V-), U1118.11 (V-)
AGND: C1105.2, C1106.2, C1107.2, C1108.2, C1110.2, C1111.2, C1112.2, C1121.2, C1122.2, C1123.2, C1124.2, C1125.2, C1126.2, C1127.2, C1128.2, C1129.2, C1130.2, C1131.2, C1132.2, C1133.2, C1134.2, C1135.2, C1136.2, C1137.2, C1138.2, C1139.2, C1140.2, C1141.2, C1142.2, C1143.2, C1144.2, C1145.2, C1146.2, C1147.2, C1148.2, C1149.2, C1150.2, C1151.2, C1152.2, C1153.2, DO1105.1 (A), J101.S (Sleeve), J102.S (Sleeve), J103.S (Sleeve), J104.S (Sleeve), J105.S (Sleeve), J106.S (Sleeve), J107.S (Sleeve), J108.S (Sleeve), Q1101.5 (B2), R1101.2, R1103.2, R1105.2, R1107.2, R1109.2, R1111.2, R1113.2, R1115.2, R1120.2, R1126.2, R1130.2, R1132.2, R1134.2, R1136.2, R1138.2, R1139.2, R1151.2, R1155.2, R1161.2, R1163.2, R1172.2, R1175.2, R1179.2, R1183.2, R1185.2, R1190.2, R1196.2, RV106.1 (CCW), RV107.1 (CCW), RV108.1 (CCW), RVO1107.2 (Wiper), RVO1107.3 (CW), RVO1108.2 (Wiper), RVO1108.3 (CW), RVO1109.3 (CW), SW102.1 (Right), U1101.5 (GND), U1101.6 (S4), U1101.7 (D4), U1101.8 (IN4), U1101.9 (IN3), U1101.10 (D3), U1101.11 (S3), U1101.14 (S2), U1101.15 (D2), U1101.16 (IN2), U1102.5 (GND), U1102.6 (S4), U1102.7 (D4), U1102.8 (IN4), U1102.9 (IN3), U1102.10 (D3), U1102.11 (S3), U1102.14 (S2), U1102.15 (D2), U1102.16 (IN2), U1103.5 (GND), U1103.6 (S4), U1103.7 (D4), U1103.8 (IN4), U1103.9 (IN3), U1103.10 (D3), U1103.11 (S3), U1103.14 (S2), U1103.15 (D2), U1103.16 (IN2), U1104.5 (GND), U1104.6 (S4), U1104.7 (D4), U1104.8 (IN4), U1104.9 (IN3), U1104.10 (D3), U1104.11 (S3), U1104.14 (S2), U1104.15 (D2), U1104.16 (IN2), U1105.12 (GND), U1106.4 (GND), U1106.5 (+), U1107.3, U1107.5, U1107.7 (GND), U1107.9, U1107.11, U1107.13, U1108.4 (GND), U1108.5 (+), U1111.10 (+), U1111.12 (+), U1113.10 (+), U1113.12 (+), U1115.5 (+), U1115.10 (+), U1115.12 (+), U1117.12 (+), U1118.5 (+), U1118.10 (+), U1118.12 (+)
BASE_ADJ: R1147.1, RVO1106.2 (Wiper)
BASE_REF5: RB1114.2, RB1115.1, RVO1106.3 (CW)
BASE_REF5_DRIVE: C1117.1, RB1114.1, U1110.8
BASE_REF5_FB: C1117.2, RB1115.2, U1110.9 (-)
BASE_REFN5: RB1116.2, RB1117.1, RVO1106.1 (CCW)
BASE_REFN5_DRIVE: C1118.1, RB1116.1, U1110.14
BASE_REFN5_FB: C1118.2, RB1117.2, U1110.13 (-)
C1b3f1d_SENSE: DO1103.3 (COM), R1112.2, U1116.5 (+)
C1e2eb4_SENSE: DO1101.3 (COM), R1104.2, U1118.3 (+)
C1eb779_SUM: C1102.2, R1121.2, R1122.2, U1112.6 (-)
C1eb779_W: R1119.1, RV106.2 (WIPER)
C1eb779_W_SENSE: R1119.2, R1120.1, U1112.5 (+)
C3f1879_SENSE: DO1102.3 (COM), R1108.2, U1116.3 (+)
C7b4ed2_DRIVE: RB1106.1, U1117.6 (-), U1117.7
C7b4ed2_ISO_MID: RB1106.2, RB1107.1
C7f1c03_ENABLE: R1101.1, R1102.2, U1101.1 (IN1)
C09b529_ENABLE: R1105.1, R1106.2, U1102.1 (IN1)
C42d8cd_SUM: C1104.2, R1127.2, R1128.2, U1112.13 (-)
C42d8cd_W: R1125.1, RV108.2 (WIPER)
C42d8cd_W_SENSE: R1125.2, R1126.1, U1112.12 (+)
C70dbdb_DRIVE: RB1102.1, U1116.13 (-), U1116.14
C70dbdb_ISO_MID: RB1102.2, RB1103.1
C83f36b_W: R1129.1, RV104.2 (WIPER)
C83f36b_W_SENSE: C1105.1, R1129.2, R1130.1, U1109.3 (+)
C99bd37_CMP_OUT: R1159.1, R1160.2, U1106.1, U1107.1
C99bd37_GATE_SENSE: R1156.2, R1157.2, U1106.2 (-)
C99bd37_THRESH: R1158.2, R1159.2, U1106.3 (+)
C461f80_DRIVE: C1103.1, R1123.1, U1112.8
C461f80_FB: C1103.2, R1124.2, U1112.9 (-)
C953c1a_DRIVE: C1101.1, R1117.1, U1112.1
C953c1a_FB: C1101.2, R1118.2, U1112.2 (-)
C7727d5_ENABLE: R1109.1, R1110.2, U1103.1 (IN1)
C807778_ENABLE: R1113.1, R1114.2, U1104.1 (IN1)
Ca449b7_W: R1133.1, RV107.2 (WIPER)
Ca449b7_W_SENSE: C1107.1, R1133.2, R1134.1, U1113.3 (+)
Cc44f2e_SENSE: DO1104.3 (COM), R1116.2, U1116.10 (+)
Cc66d82_DRIVE: RB1104.1, U1117.1, U1117.2 (-)
Cc66d82_ISO_MID: RB1104.2, RB1105.1
Ce35646_W: R1131.1, RV105.2 (WIPER)
Ce35646_W_SENSE: C1106.1, R1131.2, R1132.1, U1109.5 (+)
Cec1eaa_DRIVE: RB1108.1, U1117.8, U1117.9 (-)
Cec1eaa_ISO_MID: RB1108.2, RB1109.1
EXPO_SUM: R1140.2, R1141.2, R1142.2, R1143.2, R1144.2, R1145.2, R1146.2, R1147.2, U1105.15 (VFCI)
FINE_MANUAL: R1143.1, U1109.6 (-), U1109.7
FM_BUFFER: R1121.1, U1112.3 (+), U1116.1, U1116.2 (-)
FM_DEPTH: C1102.1, R1122.1, R1144.1, U1112.7
FM_PROTECTED: R1107.1, R1108.1, U1102.2 (D1)
FM_REMOTE: R1117.2, R1118.1, RV106.3 (CW)
FM_TIP: J102.T (Tip), U1102.3 (S1)
HARD_DRIVE: R1163.1, R1164.1, SW103.1 (Right)
HARD_EDGE: C1114.1, R1164.2
HARD_PIN: C1114.2, U1105.6 (VHSI)
HF_PIN: RVO1109.1 (CCW), U1105.7 (VHFT)
IO_EXTRA_18_IO_UNUSED2: U1118.6 (-), U1118.7
IO_EXTRA_18_IO_UNUSED3: U1118.8, U1118.9 (-)
IO_EXTRA_18_IO_UNUSED4: U1118.13 (-), U1118.14
LFO_FB: R1137.2, R1138.1, U1113.6 (-)
LFO_REF: R1137.1, SW102.3 (Left), U1113.7
LINEAR_FILTER: C1112.1, R1154.2
LINEAR_REF: R1153.2, R1154.1, RVO1109.2 (Wiper), U1105.13 (VLFI)
LOCAL_REF5: R1146.1, R1157.1, R1168.1, R1171.1, R1174.1, R1178.1, R1184.1, R1188.1, RB1110.2, RB1111.1, RV104.3 (CW), RV105.3 (CW), RV107.3 (CW)
LOCAL_REF5_DRIVE: C1115.1, RB1110.1, U1110.1
LOCAL_REF5_FB: C1115.2, RB1111.2, U1110.2 (-)
LOCAL_REFN5: RB1112.2, RB1113.1, RV104.1 (CCW), RV105.1 (CCW), U1109.12 (+), U1113.5 (+)
LOCAL_REFN5_DRIVE: C1116.1, RB1112.1, U1110.7
LOCAL_REFN5_FB: C1116.2, RB1113.2, U1110.6 (-)
OCT_CV: R1141.1, U1109.8, U1109.9 (-)
OCT_FILTER: C1108.1, R1135.2, R1136.1, U1109.10 (+)
OCT_SELECTED: R1135.1, SW101.1 (COMMON_A), SW101.10 (COMMON_B)
OSC_GATE_REF: R1158.1
OSC_OCT0: SW101.2 (POS1)
OSC_OCT1: SW101.3 (POS2)
OSC_OCT2: SW101.4 (POS3)
OSC_OCT3: SW101.5 (POS4)
OSC_OCT4: SW101.6 (POS5)
OSC_OCT5: SW101.7 (POS6)
OSC_REF5: U1110.3 (+), U1110.10 (+), U1111.3 (+)
OSC_REFN5: U1110.5 (+), U1110.12 (+), U1111.5 (+)
PACK_OPA4196IDR_3_IO_UNUSED3: U1115.8, U1115.9 (-)
PACK_OPA4196IDR_3_IO_UNUSED4: U1115.13 (-), U1115.14
PACK_OPA4196IDR_5_IO_UNUSED4: U1117.13 (-), U1117.14
PACK_OPA4197IPWR_2_IO_UNUSED3: U1111.8, U1111.9 (-)
PACK_OPA4197IPWR_2_IO_UNUSED4: U1111.13 (-), U1111.14
PULSE_HALF: R1182.2, R1183.1, U1108.2 (-)
PULSE_LOGIC: R1186.2, U1108.1, U1114.12 (+)
PULSE_RAW: R1155.1, R1182.1, U1105.4 (VP)
PUL_SCALED: R1187.1, U1114.14, U1117.10 (+)
PUL_SUM: R1187.2, R1188.2, U1114.13 (-)
PUL_TIP: J108.T (Tip), RB1109.2
PWM_BUFFER: R1127.1, U1112.10 (+), U1116.6 (-), U1116.7
PWM_DEPTH: C1104.1, R1128.1, R1167.1, U1112.14
PWM_DRIVE: R1170.1, R1173.1, U1113.14
PWM_INV: R1169.2, R1170.2, U1113.13 (-)
PWM_NEG: R1165.1, R1169.1, U1113.8
PWM_PIN: DO1105.3 (COM), R1173.2, U1105.5 (VPWM)
PWM_PROTECTED: R1111.1, R1112.1, U1103.2 (D1)
PWM_REMOTE: R1123.2, R1124.1, RV108.3 (CW)
PWM_SUM: R1165.2, R1166.2, R1167.2, R1168.2, U1113.9 (-)
PWM_TIP: J103.T (Tip), U1103.3 (S1)
PW_MANUAL: R1166.1, U1113.1, U1113.2 (-)
RANGE_CV: R1139.1, R1145.1, SW102.2 (Common)
REF4: DO1105.2 (K), U1114.1, U1114.2 (-)
REF4_RAW: R1171.2, R1172.1, U1114.3 (+)
REF25: R1184.2, R1185.1, U1108.3 (+)
RZ_TRIM: R1150.2, RVO1107.1 (CCW)
SAW_BIAS: R1178.2, R1179.1, U1114.10 (+)
SAW_RAW: R1180.1, U1105.8 (VSO)
SAW_SCALED: R1181.1, U1114.8, U1117.5 (+)
SAW_SUM: R1180.2, R1181.2, U1114.9 (-)
SAW_TIP: J107.T (Tip), RB1107.2
SCALE1: R1150.1, U1105.1 (SCALE1)
SCALE2: R1151.1, U1105.2 (SCALE2)
SCALE_ADJ: R1152.2, RVO1108.1 (CCW)
SCALE_PIN: C1110.1, R1152.1, U1105.14 (VS)
SINE_BASE: Q1101.2 (B1), R1189.2, R1190.1, R1191.2
SINE_C1: Q1101.6 (C1), R1193.2, R1197.1
SINE_C2: Q1101.3 (C2), R1194.2, R1195.1
SINE_DIFF: R1198.1, R1199.1, U1115.1
SINE_GAIN_SUM: R1199.2, RVO1111.2 (Wiper), RVO1111.3 (CW), U1115.6 (-)
SINE_GAIN_TRIM: RB1101.2, RVO1111.1 (CCW)
SINE_MINUS: R1197.2, R1198.2, U1115.2 (-)
SINE_OFFSET: R1191.1, RVO1110.2 (Wiper)
SINE_PLUS: R1195.2, R1196.1, U1115.3 (+)
SINE_REF5: RB1118.2, RB1119.1, RVO1110.3 (CW)
SINE_REF5_DRIVE: C1119.1, RB1118.1, U1111.1
SINE_REF5_FB: C1119.2, RB1119.2, U1111.2 (-)
SINE_REFN5: RB1120.2, RB1121.1, RVO1110.1 (CCW)
SINE_REFN5_DRIVE: C1120.1, RB1120.1, U1111.7
SINE_REFN5_FB: C1120.2, RB1121.2, U1111.6 (-)
SINE_TAIL: Q1101.1 (E1), Q1101.4 (E2), R1192.1
SIN_SCALED: RB1101.1, U1115.7, U1116.12 (+)
SIN_TIP: J105.T (Tip), RB1103.2
SOFT_DRIVE: R1161.1, R1162.1, SW103.3 (Left)
SOFT_EDGE: C1113.1, R1162.2
SOFT_PIN: C1113.2, U1105.9 (VSSI)
SYNC_BUFFER: R1156.1, U1116.8, U1116.9 (-)
SYNC_GATE: SW103.2 (Common), U1107.2
SYNC_PROTECTED: R1115.1, R1116.1, U1104.2 (D1)
SYNC_TIP: J104.T (Tip), U1104.3 (S1)
TIMING_CAP: C1111.1, U1105.11 (CAP)
TRI_BIAS: R1174.2, R1175.1, U1114.5 (+)
TRI_RAW: R1176.1, U1105.10 (VTO)
TRI_SCALED: R1177.1, R1189.1, U1114.7, U1117.3 (+)
TRI_SUM: R1176.2, R1177.2, U1114.6 (-)
TRI_TIP: J106.T (Tip), RB1105.2
TUNE_MANUAL: R1142.1, U1109.1, U1109.2 (-)
VEE5: C1130.1, R1148.2, R1149.1, U1105.3 (VEE)
VEE_DRIVE: C1109.1, R1148.1, U1109.14
VEE_FB: C1109.2, R1149.2, U1109.13 (-)
