Takazudo/zudo-osc-hole-field/schematic/sheets/sample_hold.kicad_sch

## KiCad design schematic/sheets/sample_hold.kicad_sch (2026-10-02)

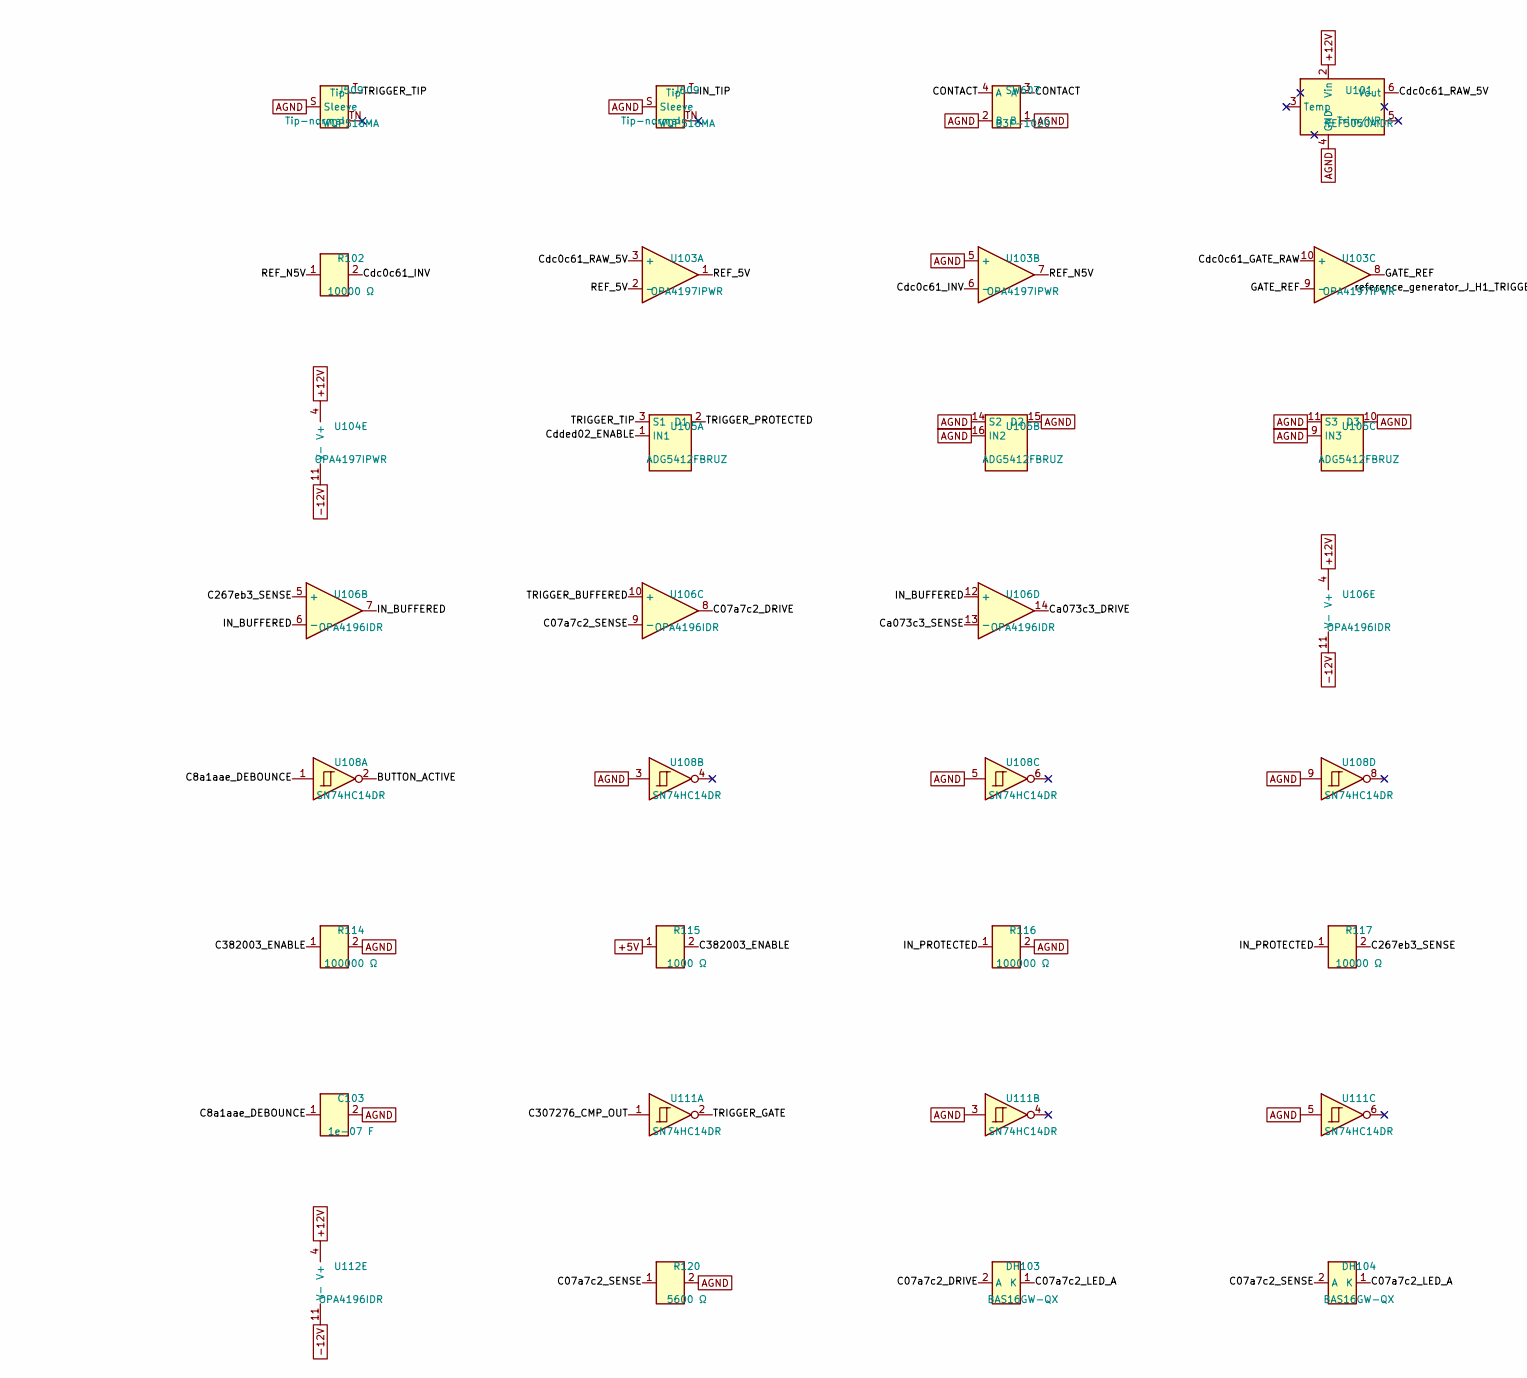
[picture p143: schematic sample_hold.kicad_sch, part in row 1, column 1]

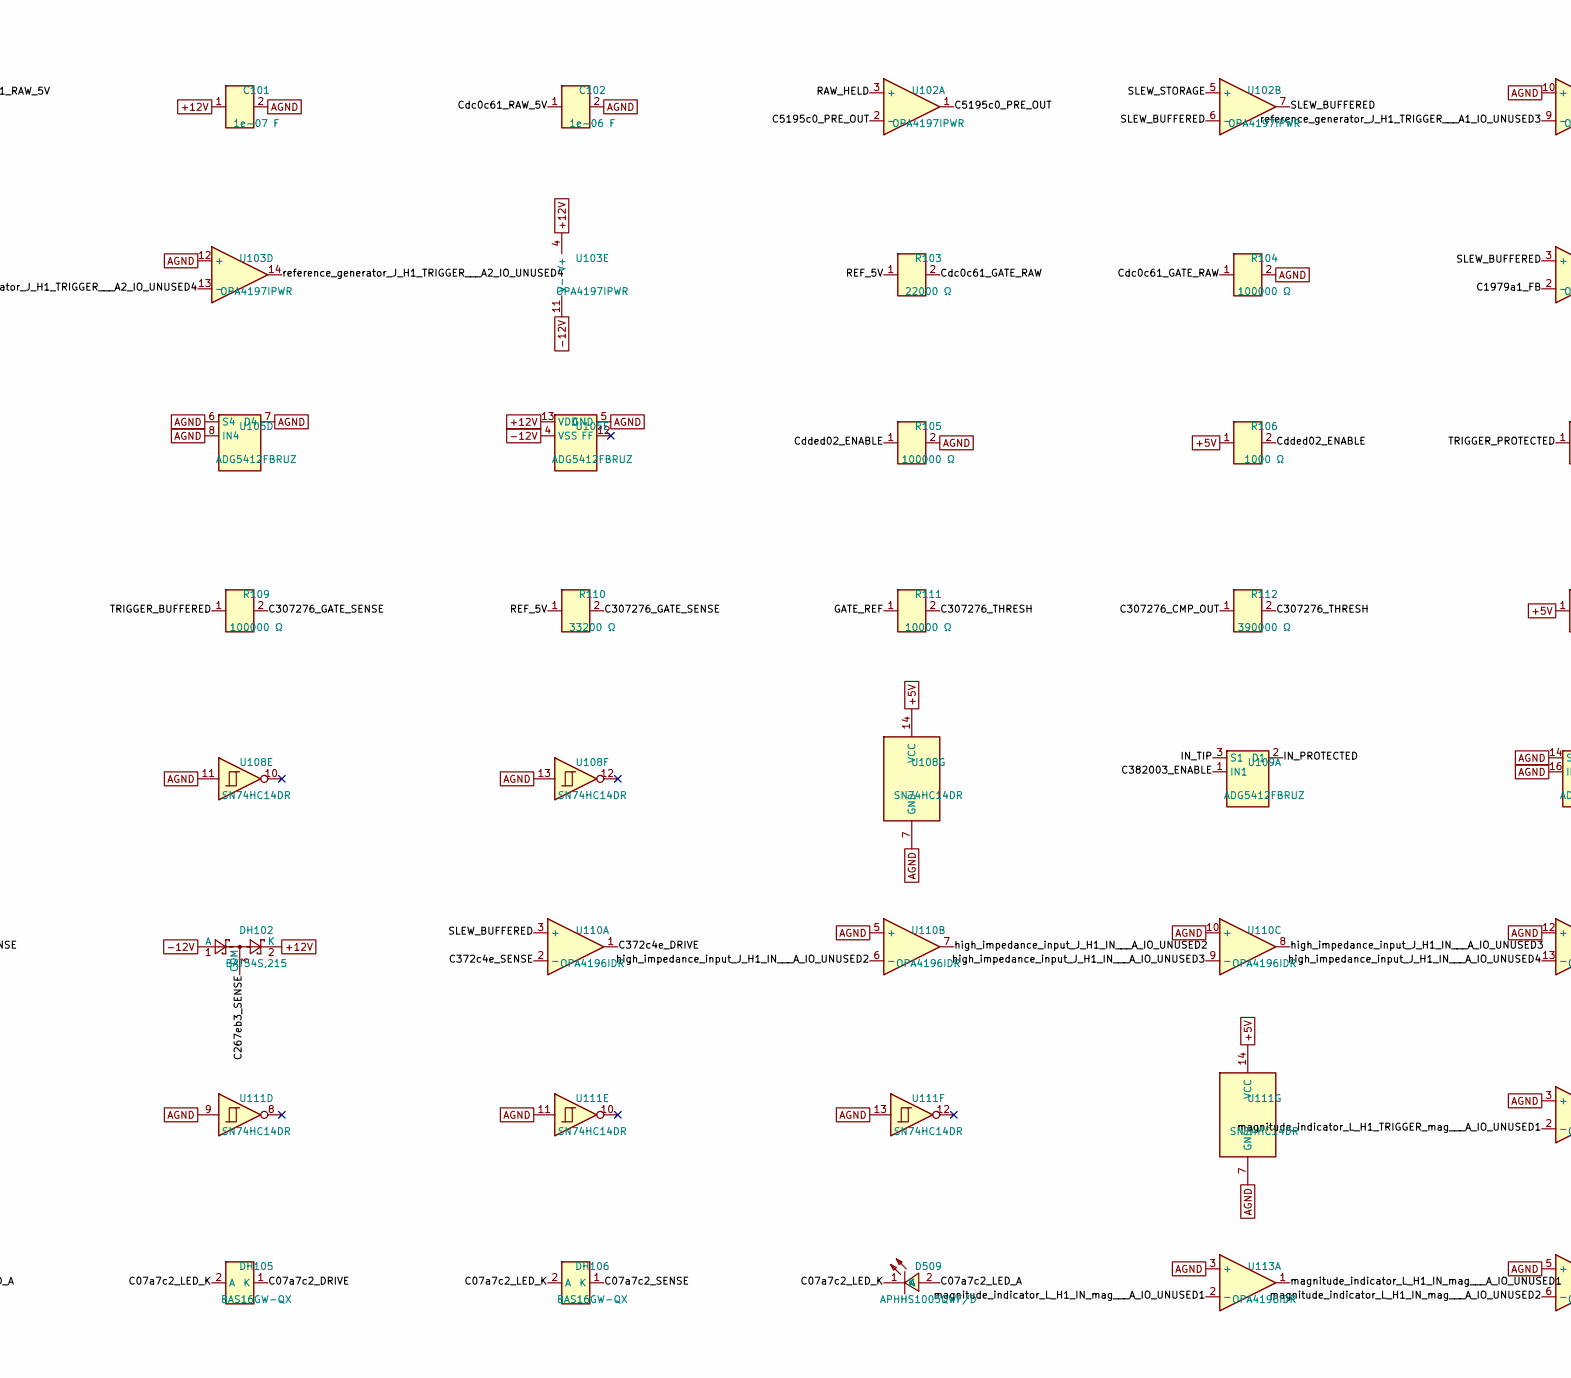
[picture p144: schematic sample_hold.kicad_sch, part in row 1, column 2]

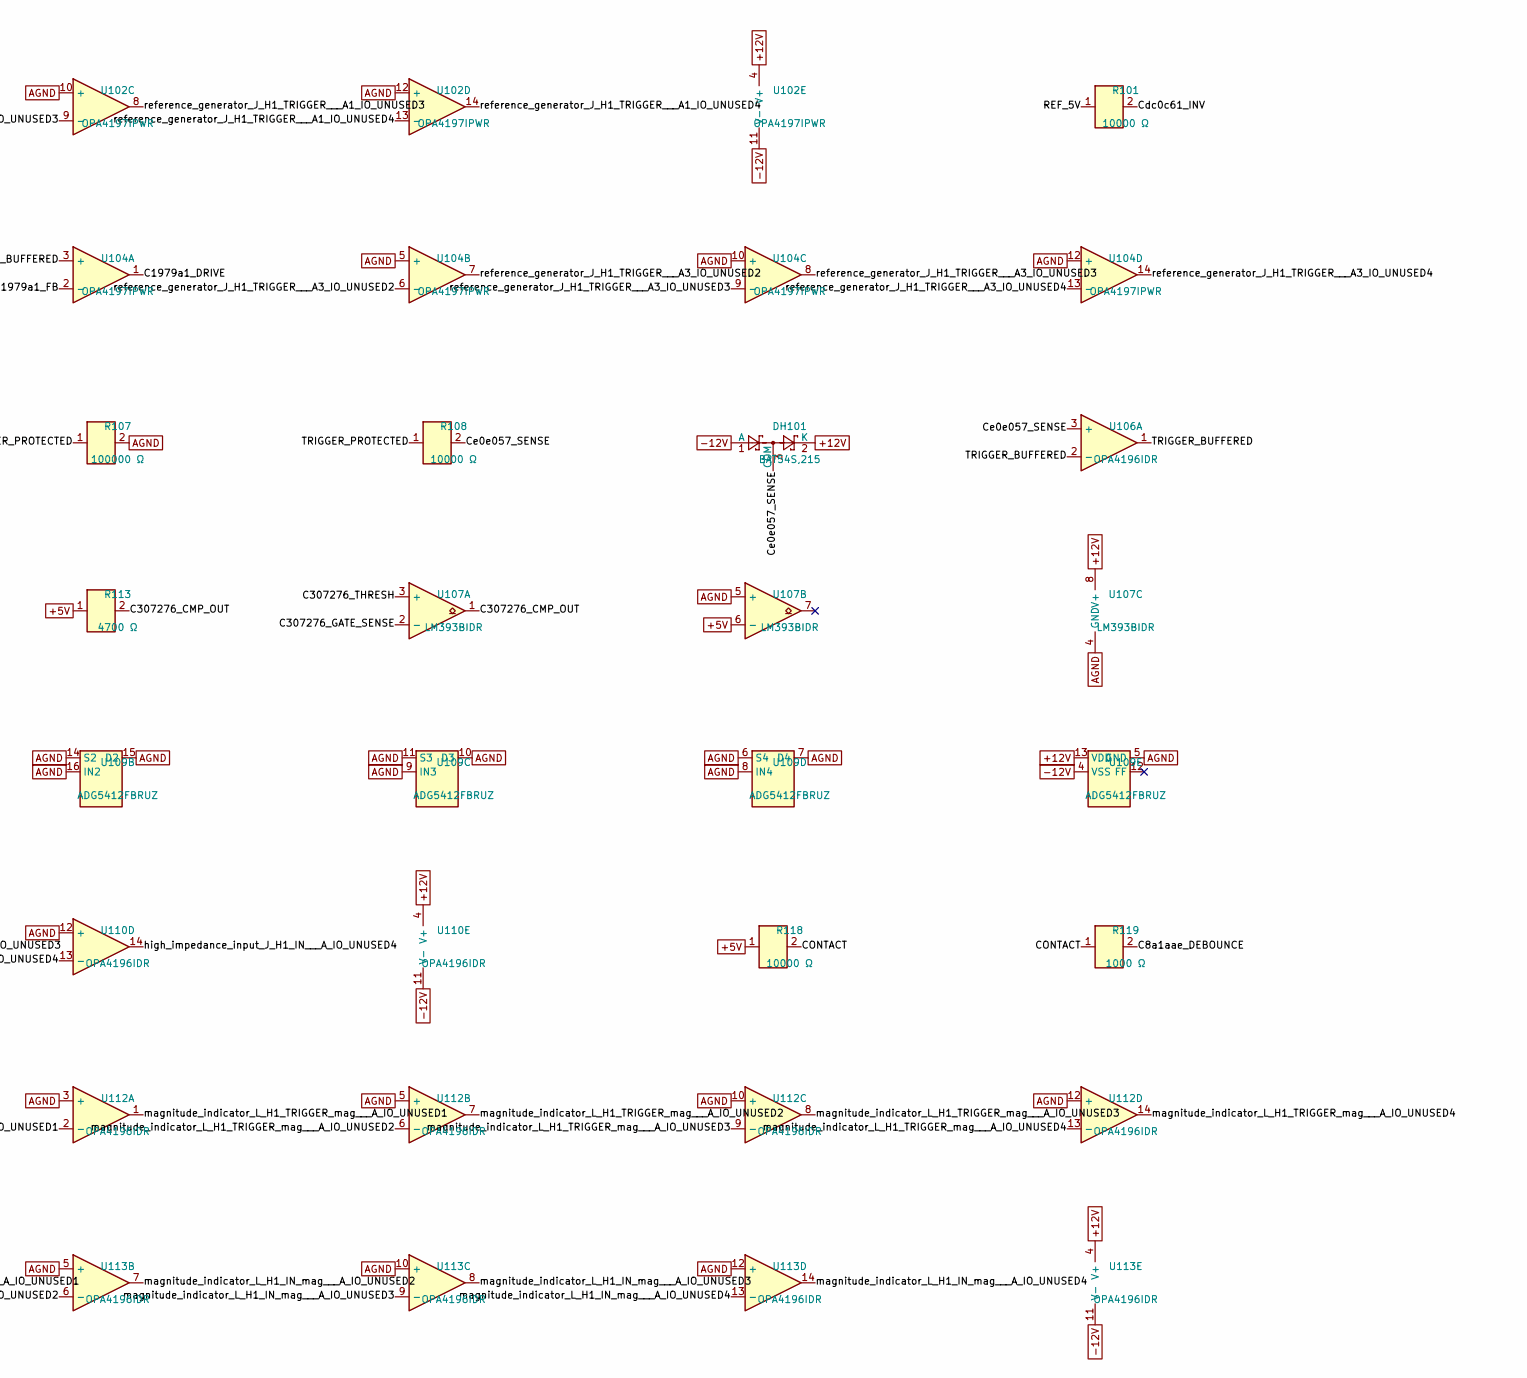
[picture p145: schematic sample_hold.kicad_sch, part in row 1, column 3]

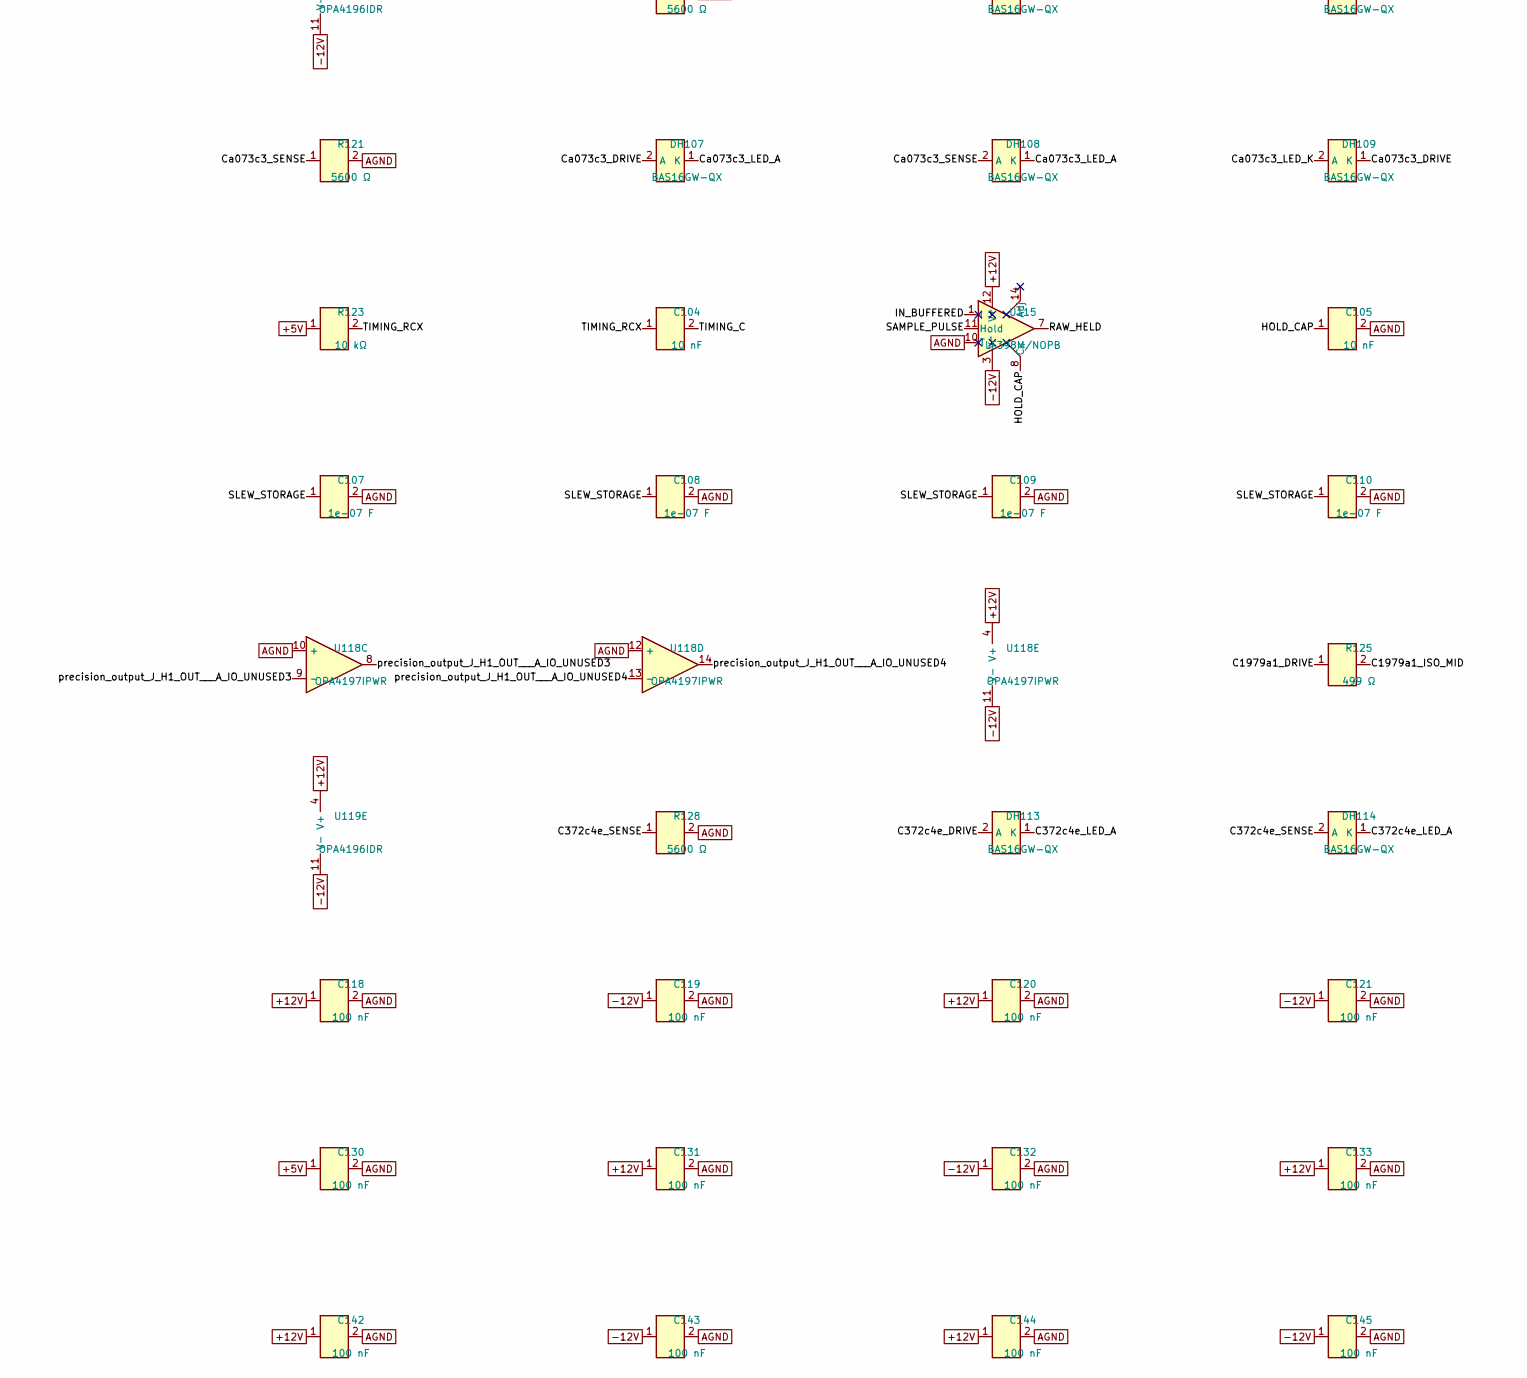
[picture p146: schematic sample_hold.kicad_sch, part in row 2, column 1]

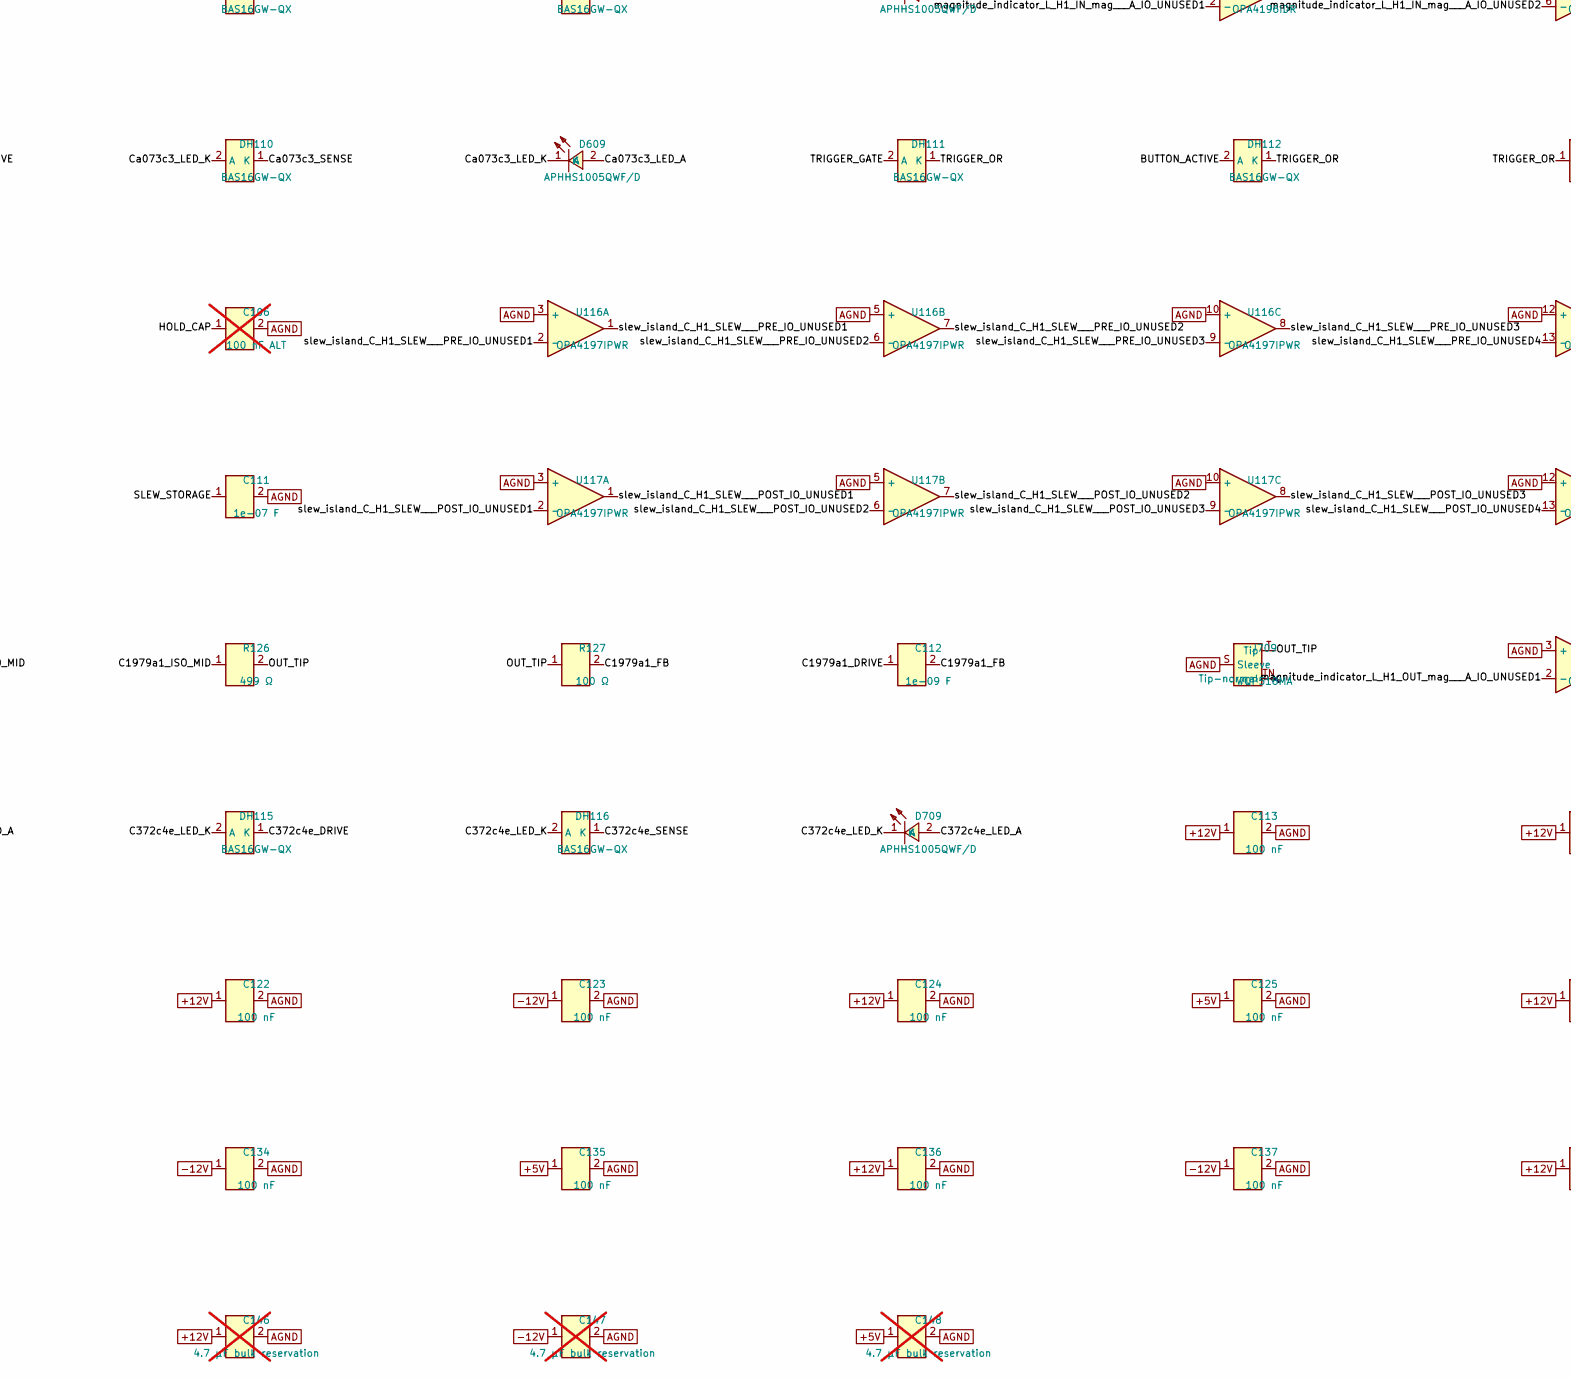
[picture p147: schematic sample_hold.kicad_sch, part in row 2, column 2]

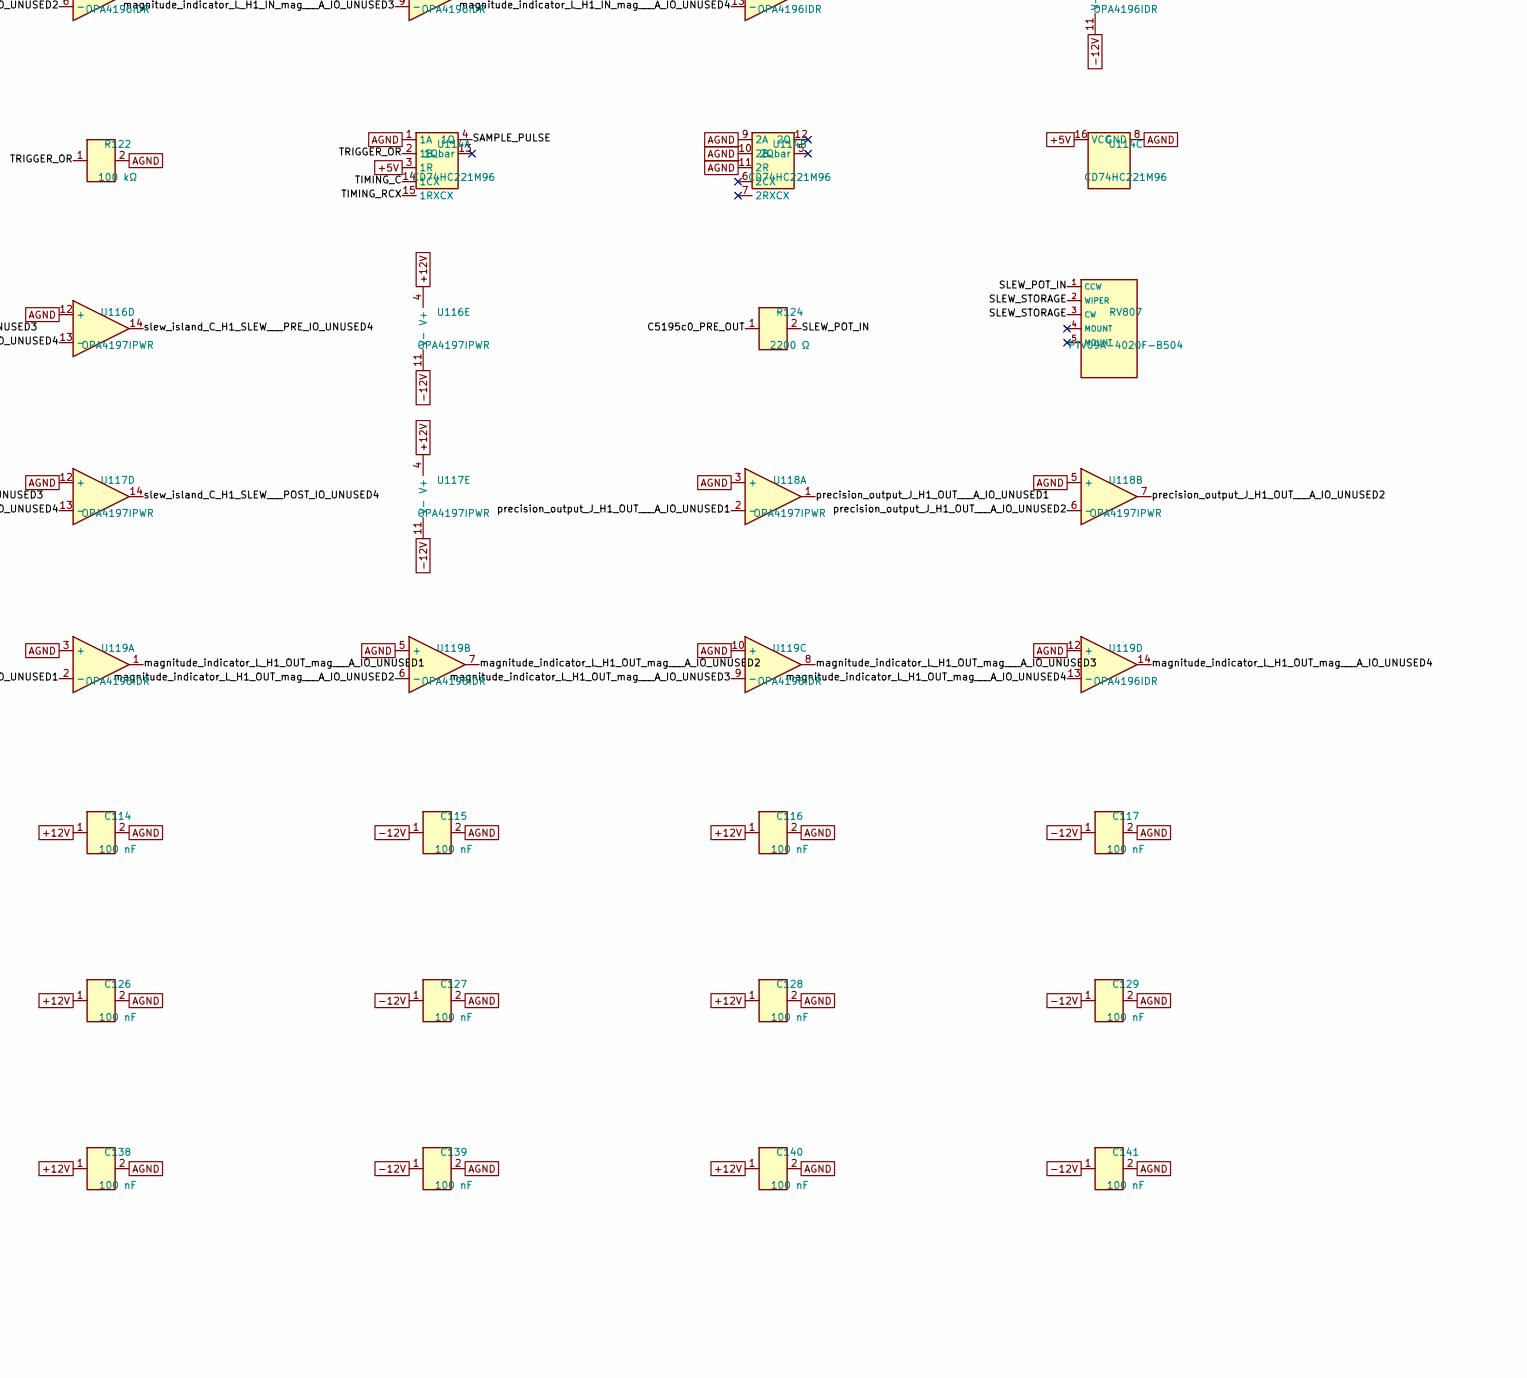
[picture p148: schematic sample_hold.kicad_sch, part in row 2, column 3]

Parts:
C101, C103: 1e-07 F; C0603; MPN GRM188R71H104KA93D
C102: 1e-06 F; C0603
C104, C105: 10 nF; C0805; MPN C0805C103J5GACTU; LCSC C2167597
C106: 100 nF ALT; C0805; not fitted
C107, C108, C109, C110, C111: 1e-07 F; C1206; MPN 1206CG104J500NT; LCSC C46348
C112: 1e-09 F; C0603; MPN C0603C102J5GACTU
C113, C114, C115, C116, C117, C118, C119, C120, C121, C122, C123, C124, C125, C126, C127, C128, C129, C130, C131, C132, C133, C134, C135, C136, C137, C138, C139, C140, C141, C142, C143, C144, C145: 100 nF; C0603; MPN GRM188R71H104KA93D
C146, C147, C148: 4.7 µF bulk reservation; C0805; MPN GRM21BR61E475KA12L; not fitted
D509, D609, D709: APHHS1005QWF/D; LED0402-Kingbright-White; MPN APHHS1005QWF/D
DH101, DH102: BAT54S,215; SOT-23; MPN BAT54S,215
DH103, DH104, DH105, DH106, DH107, DH108, DH109, DH110, DH111, DH112, DH113, DH114, DH115, DH116: BAS16GW-QX; SOD-123; MPN BAS16GW-QX
J509, J609, J709: WQP518MA; Jack_3.5mm_QingPu_WQP518MA; MPN WQP518MA
R101, R102, R108, R111, R117, R118: 10000 Ω; R0603
R103: 22000 Ω; R0603
R104, R109: 100000 Ω; R0603; MPN RT0603BRD07100KL
R105, R107, R114, R116: 100000 Ω; R0603; MPN RC0603FR-07100KL
R106, R115, R119: 1000 Ω; R0603
R110: 33200 Ω; R0603
R112: 390000 Ω; R0603
R113: 4700 Ω; R0603
R120, R121, R128: 5600 Ω; R0603
R122: 100 kΩ; R0603; MPN RC0603FR-07100KL
R123: 10 kΩ; R0603
R124: 2200 Ω; R0603
R125, R126: 499 Ω; R_1210_3225Metric; MPN RC1210FR-07499RL
R127: 100 Ω; R0603; MPN RC0603FR-07100RL
RV807: PTV09A-4020F-B504; PTV09A-4020F; MPN PTV09A-4020F-B504; LCSC C5154140
SW607: B3F-1020; Button_Omron_B3F_6x6_P6.5x4.5; MPN B3F-1020; LCSC C722171
U101: REF5050AIDR; SOIC-8_3.9x4.9mm_P1.27mm; MPN REF5050AIDR; LCSC C27804
U102, U103, U104, U116, U117, U118: OPA4197IPWR; TSSOP-14_4.4x5mm_P0.65mm; MPN OPA4197IPWR; LCSC C2057327
U105, U109: ADG5412FBRUZ; TSSOP-16_4.4x5mm_P0.65mm; MPN ADG5412FBRUZ; LCSC C579073
U106, U110, U112, U113, U119: OPA4196IDR; SOIC-14_3.9x8.7mm_P1.27mm; MPN OPA4196IDR; LCSC C2057385
U107: LM393BIDR; SOIC-8_3.9x4.9mm_P1.27mm; MPN LM393BIDR
U108, U111: SN74HC14DR; SOIC-14_3.9x8.7mm_P1.27mm; MPN SN74HC14DR
U114: CD74HC221M96; SOIC-16_3.9x9.9mm_P1.27mm; MPN CD74HC221M96; LCSC C133954
U115: LF398M/NOPB; SOIC-14_3.9x8.7mm_P1.27mm; MPN LF398M/NOPB; LCSC C1346172

Connections:
+5V: C125.1, C130.1, C135.1, C148.1, R106.1, R113.1, R115.1, R118.1, R123.1, U107.6 (-), U108.14 (VCC), U111.14 (VCC), U114.3 (1R), U114.16 (VCC)
+12V: C101.1, C113.1, C114.1, C116.1, C118.1, C120.1, C122.1, C124.1, C126.1, C128.1, C131.1, C133.1, C136.1, C138.1, C140.1, C142.1, C144.1, C146.1, DH101.2 (K), DH102.2 (K), U101.2 (Vin), U102.4 (V+), U103.4 (V+), U104.4 (V+), U105.13 (VDD), U106.4 (V+), U107.8 (V+), U109.13 (VDD), U110.4 (V+), U112.4 (V+), U113.4 (V+), U115.12 (V^{+}), U116.4 (V+), U117.4 (V+), U118.4 (V+), U119.4 (V+)
-12V: C115.1, C117.1, C119.1, C121.1, C123.1, C127.1, C129.1, C132.1, C134.1, C137.1, C139.1, C141.1, C143.1, C145.1, C147.1, DH101.1 (A), DH102.1 (A), U102.11 (V-), U103.11 (V-), U104.11 (V-), U105.4 (VSS), U106.11 (V-), U109.4 (VSS), U110.11 (V-), U112.11 (V-), U113.11 (V-), U115.3 (V^{-}), U116.11 (V-), U117.11 (V-), U118.11 (V-), U119.11 (V-)
AGND: C101.2, C102.2, C103.2, C105.2, C106.2, C107.2, C108.2, C109.2, C110.2, C111.2, C113.2, C114.2, C115.2, C116.2, C117.2, C118.2, C119.2, C120.2, C121.2, C122.2, C123.2, C124.2, C125.2, C126.2, C127.2, C128.2, C129.2, C130.2, C131.2, C132.2, C133.2, C134.2, C135.2, C136.2, C137.2, C138.2, C139.2, C140.2, C141.2, C142.2, C143.2, C144.2, C145.2, C146.2, C147.2, C148.2, J509.S (Sleeve), J609.S (Sleeve), J709.S (Sleeve), R104.2, R105.2, R107.2, R114.2, R116.2, R120.2, R121.2, R122.2, R128.2, SW607.1 (B), SW607.2 (B), U101.4 (GND), U102.10 (+), U102.12 (+), U103.5 (+), U103.12 (+), U104.5 (+), U104.10 (+), U104.12 (+), U105.5 (GND), U105.6 (S4), U105.7 (D4), U105.8 (IN4), U105.9 (IN3), U105.10 (D3), U105.11 (S3), U105.14 (S2), U105.15 (D2), U105.16 (IN2), U107.4 (GND), U107.5 (+), U108.3, U108.5, U108.7 (GND), U108.9, U108.11, U108.13, U109.5 (GND), U109.6 (S4), U109.7 (D4), U109.8 (IN4), U109.9 (IN3), U109.10 (D3), U109.11 (S3), U109.14 (S2), U109.15 (D2), U109.16 (IN2), U110.5 (+), U110.10 (+), U110.12 (+), U111.3, U111.5, U111.7 (GND), U111.9, U111.11, U111.13, U112.3 (+), U112.5 (+), U112.10 (+), U112.12 (+), U113.3 (+), U113.5 (+), U113.10 (+), U113.12 (+), U114.1 (1A), U114.8 (GND), U114.9 (2A), U114.10 (2B), U114.11 (2R), U115.10 (T), U116.3 (+), U116.5 (+), U116.10 (+), U116.12 (+), U117.3 (+), U117.5 (+), U117.10 (+), U117.12 (+), U118.3 (+), U118.5 (+), U118.10 (+), U118.12 (+), U119.3 (+), U119.5 (+), U119.10 (+), U119.12 (+)
BUTTON_ACTIVE: DH112.2 (A), U108.2
C07a7c2_DRIVE: DH103.2 (A), DH105.1 (K), U106.8
C07a7c2_LED_A: D509.2 (A), DH103.1 (K), DH104.1 (K)
C07a7c2_LED_K: D509.1 (K), DH105.2 (A), DH106.2 (A)
C07a7c2_SENSE: DH104.2 (A), DH106.1 (K), R120.1, U106.9 (-)
C8a1aae_DEBOUNCE: C103.1, R119.2, U108.1
C267eb3_SENSE: DH102.3 (COM), R117.2, U106.5 (+)
C372c4e_DRIVE: DH113.2 (A), DH115.1 (K), U110.1
C372c4e_LED_A: D709.2 (A), DH113.1 (K), DH114.1 (K)
C372c4e_LED_K: D709.1 (K), DH115.2 (A), DH116.2 (A)
C372c4e_SENSE: DH114.2 (A), DH116.1 (K), R128.1, U110.2 (-)
C1979a1_DRIVE: C112.1, R125.1, U104.1
C1979a1_FB: C112.2, R127.2, U104.2 (-)
C1979a1_ISO_MID: R125.2, R126.1
C5195c0_PRE_OUT: R124.1, U102.1, U102.2 (-)
C307276_CMP_OUT: R112.1, R113.2, U107.1, U111.1
C307276_GATE_SENSE: R109.2, R110.2, U107.2 (-)
C307276_THRESH: R111.2, R112.2, U107.3 (+)
C382003_ENABLE: R114.1, R115.2, U109.1 (IN1)
CONTACT: R118.2, R119.1, SW607.3 (A), SW607.4 (A)
Ca073c3_DRIVE: DH107.2 (A), DH109.1 (K), U106.14
Ca073c3_LED_A: D609.2 (A), DH107.1 (K), DH108.1 (K)
Ca073c3_LED_K: D609.1 (K), DH109.2 (A), DH110.2 (A)
Ca073c3_SENSE: DH108.2 (A), DH110.1 (K), R121.1, U106.13 (-)
Cdc0c61_GATE_RAW: R103.2, R104.1, U103.10 (+)
Cdc0c61_INV: R101.2, R102.2, U103.6 (-)
Cdc0c61_RAW_5V: C102.1, U101.6 (Vout), U103.3 (+)
Cdded02_ENABLE: R105.1, R106.2, U105.1 (IN1)
Ce0e057_SENSE: DH101.3 (COM), R108.2, U106.3 (+)
GATE_REF: R111.1, U103.8, U103.9 (-)
HOLD_CAP: C105.1, C106.1, U115.8 (C_{h})
IN_BUFFERED: U106.6 (-), U106.7, U106.12 (+), U115.1 (I)
IN_PROTECTED: R116.1, R117.1, U109.2 (D1)
IN_TIP: J609.T (Tip), U109.3 (S1)
OUT_TIP: J709.T (Tip), R126.2, R127.1
RAW_HELD: U102.3 (+), U115.7
REF_5V: R101.1, R103.1, R110.1, U103.1, U103.2 (-)
REF_N5V: R102.1, U103.7
SAMPLE_PULSE: U114.4 (1Q), U115.11 (Hold)
SLEW_BUFFERED: U102.6 (-), U102.7, U104.3 (+), U110.3 (+)
SLEW_POT_IN: R124.2, RV807.1 (CCW)
SLEW_STORAGE: C107.1, C108.1, C109.1, C110.1, C111.1, RV807.2 (WIPER), RV807.3 (CW), U102.5 (+)
TIMING_C: C104.2, U114.14 (1CX)
TIMING_RCX: C104.1, R123.2, U114.15 (1RXCX)
TRIGGER_BUFFERED: R109.1, U106.1, U106.2 (-), U106.10 (+)
TRIGGER_GATE: DH111.2 (A), U111.2
TRIGGER_OR: DH111.1 (K), DH112.1 (K), R122.1, U114.2 (1B)
TRIGGER_PROTECTED: R107.1, R108.1, U105.2 (D1)
TRIGGER_TIP: J509.T (Tip), U105.3 (S1)
high_impedance_input_J_H1_IN___A_IO_UNUSED2: U110.6 (-), U110.7
high_impedance_input_J_H1_IN___A_IO_UNUSED3: U110.8, U110.9 (-)
high_impedance_input_J_H1_IN___A_IO_UNUSED4: U110.13 (-), U110.14
magnitude_indicator_L_H1_IN_mag___A_IO_UNUSED1: U113.1, U113.2 (-)
magnitude_indicator_L_H1_IN_mag___A_IO_UNUSED2: U113.6 (-), U113.7
magnitude_indicator_L_H1_IN_mag___A_IO_UNUSED3: U113.8, U113.9 (-)
magnitude_indicator_L_H1_IN_mag___A_IO_UNUSED4: U113.13 (-), U113.14
magnitude_indicator_L_H1_OUT_mag___A_IO_UNUSED1: U119.1, U119.2 (-)
magnitude_indicator_L_H1_OUT_mag___A_IO_UNUSED2: U119.6 (-), U119.7
magnitude_indicator_L_H1_OUT_mag___A_IO_UNUSED3: U119.8, U119.9 (-)
magnitude_indicator_L_H1_OUT_mag___A_IO_UNUSED4: U119.13 (-), U119.14
magnitude_indicator_L_H1_TRIGGER_mag___A_IO_UNUSED1: U112.1, U112.2 (-)
magnitude_indicator_L_H1_TRIGGER_mag___A_IO_UNUSED2: U112.6 (-), U112.7
magnitude_indicator_L_H1_TRIGGER_mag___A_IO_UNUSED3: U112.8, U112.9 (-)
magnitude_indicator_L_H1_TRIGGER_mag___A_IO_UNUSED4: U112.13 (-), U112.14
precision_output_J_H1_OUT___A_IO_UNUSED1: U118.1, U118.2 (-)
precision_output_J_H1_OUT___A_IO_UNUSED2: U118.6 (-), U118.7
precision_output_J_H1_OUT___A_IO_UNUSED3: U118.8, U118.9 (-)
precision_output_J_H1_OUT___A_IO_UNUSED4: U118.13 (-), U118.14
reference_generator_J_H1_TRIGGER___A1_IO_UNUSED3: U102.8, U102.9 (-)
reference_generator_J_H1_TRIGGER___A1_IO_UNUSED4: U102.13 (-), U102.14
reference_generator_J_H1_TRIGGER___A2_IO_UNUSED4: U103.13 (-), U103.14
reference_generator_J_H1_TRIGGER___A3_IO_UNUSED2: U104.6 (-), U104.7
reference_generator_J_H1_TRIGGER___A3_IO_UNUSED3: U104.8, U104.9 (-)
reference_generator_J_H1_TRIGGER___A3_IO_UNUSED4: U104.13 (-), U104.14
slew_island_C_H1_SLEW___POST_IO_UNUSED1: U117.1, U117.2 (-)
slew_island_C_H1_SLEW___POST_IO_UNUSED2: U117.6 (-), U117.7
slew_island_C_H1_SLEW___POST_IO_UNUSED3: U117.8, U117.9 (-)
slew_island_C_H1_SLEW___POST_IO_UNUSED4: U117.13 (-), U117.14
slew_island_C_H1_SLEW___PRE_IO_UNUSED1: U116.1, U116.2 (-)
slew_island_C_H1_SLEW___PRE_IO_UNUSED2: U116.6 (-), U116.7
slew_island_C_H1_SLEW___PRE_IO_UNUSED3: U116.8, U116.9 (-)
slew_island_C_H1_SLEW___PRE_IO_UNUSED4: U116.13 (-), U116.14
