Takazudo/zudo-osc-hole-field/schematic/sheets/wavefolder.kicad_sch

## KiCad design schematic/sheets/wavefolder.kicad_sch (2026-09-30)

Schematic: wavefolder.kicad_sch

Parts:
C5101: 1e-07 F; C0603; MPN GRM188R71H104KA93D
C5102: 1e-06 F; C0603
C5103, C5104: 1e-08 F; C0603
C5105, C5118: 1e-10 F; C0603; MPN C0603C101J5GACTU
C5106: 1e-11 F; C0603
C5107: 100 pF; C0603; MPN C0603C101J5GACTU
C5108, C5109, C5110, C5111, C5112, C5113, C5114, C5115, C5116, C5117: 100 nF C0G; C1206; MPN 1206CG104J500NT; LCSC C46348
C5119, C5120, C5121, C5122, C5123, C5124, C5125, C5126, C5127, C5128, C5129, C5130, C5131, C5132, C5133, C5134, C5135, C5136, C5137, C5138, C5139, C5140, C5141, C5142, C5143: 100 nF; C0603; MPN GRM188R71H104KA93D
D907, D908, D1007: APHHS1005QWF/D; LED0402-Kingbright-White; MPN APHHS1005QWF/D
D5101, D5102, D5103, D5104: BAT54S,215; SOT-23; MPN BAT54S,215
D5105, D5106, D5107, D5108, D5109, D5110, D5111, D5112, D5113, D5114, D5115, D5116, D5117, D5119, D5120, D5121, D5122, D5124, D5125, D5126, D5127: BAS16GW-QX; SOD-123; MPN BAS16GW-QX
J907, J908, J1007, J1008: WQP518MA; Jack_3.5mm_QingPu_WQP518MA; MPN WQP518MA
Q5101: MMBT3906,215; SOT-23; MPN MMBT3906,215
R5101, R5102, R5108, R5112, R5116, R5122, R5168: 10000 Ω; R0603
R5103: 22000 Ω; R0603
R5104, R5125, R5126: 100000 Ω; R0603; MPN RT0603BRD07100KL
R5105, R5107, R5109, R5111, R5113, R5115: 100000 Ω; R0603; MPN RC0603FR-07100KL
R5106, R5110, R5114, R5117, R5119, R5123, R5169: 1000 Ω; R0603
R5118, R5120, R5124, R5170: 1e+07 Ω; R0603
R5121, R5167: 100 Ω; R0603
R5127, R5128, R5129, R5130, R5131, R5133, R5134, R5135, R5136, R5140, R5144, R5146, R5149, R5150, R5151, R5153, R5154, R5156, R5157, R5159, R5160, R5162, R5163, R5166: 100 kΩ; R0603; MPN RT0603BRD07100KL
R5132, R5138, R5152, R5155, R5158, R5161, R5165: 10 kΩ; R0603
R5137: 12.4 kΩ; R0603
R5139: 22 kΩ; R0603
R5141: 200 Ω; R0603
R5142: 470 kΩ; R0603
R5143: 1 kΩ; R0603
R5145: 49.9 kΩ; R0603
R5147, R5148: 1 MΩ; R0603
R5164: 70 kΩ; R0603
R5171, R5172: 499 Ω; R_1210_3225Metric; MPN RC1210FR-07499RL
R5173, R5174, R5175: 5600 Ω; R0603
RV907, RV908: PTV09A-4020F-B104; PTV09A-4020F; MPN PTV09A-4020F-B104
RV1007, RV1008: PTV09A-4020F-B103; PTV09A-4020F; MPN PTV09A-4020F-B103; LCSC C5848782
RV5104, RV5105: 10 kΩ; Potentiometer_Bourns_TC33X_Vertical; MPN TC33X-2-103E
U5101: REF5050AIDR; SOIC-8_3.9x4.9mm_P1.27mm; MPN REF5050AIDR; LCSC C27804
U5102, U5103, U5104: ADG5412FBRUZ; TSSOP-16_4.4x5mm_P0.65mm; MPN ADG5412FBRUZ; LCSC C579073
U5105: LM13700M/NOPB; SOIC-16_3.9x9.9mm_P1.27mm; MPN LM13700M/NOPB; LCSC C1346265
U5106: OPA4197IPWR; TSSOP-14_4.4x5mm_P0.65mm; MPN OPA4197IPWR; LCSC C2057327
U5107, U5108, U5109, U5110, U5111, U5112, U5113: OPA4196IDR; SOIC-14_3.9x8.7mm_P1.27mm; MPN OPA4196IDR; LCSC C2057385

Connections:
+5V: R5106.1, R5110.1, R5114.1
+12V: C5101.1, C5119.1, C5120.1, C5122.1, C5124.1, C5126.1, C5128.1, C5130.1, C5132.1, C5134.1, C5136.1, C5138.1, C5140.1, C5142.1, D5101.2 (K), D5102.2 (K), D5103.2 (K), U5101.2 (Vin), U5102.13 (VDD), U5103.13 (VDD), U5104.13 (VDD), U5105.11 (V+), U5106.4 (V+), U5107.4 (V+), U5108.4 (V+), U5109.4 (V+), U5110.4 (V+), U5111.4 (V+), U5112.4 (V+), U5113.4 (V+)
-12V: C5121.1, C5123.1, C5125.1, C5127.1, C5129.1, C5131.1, C5133.1, C5135.1, C5137.1, C5139.1, C5141.1, C5143.1, D5101.1 (A), D5102.1 (A), D5103.1 (A), R5144.2, U5102.4 (VSS), U5103.4 (VSS), U5104.4 (VSS), U5105.6 (V-), U5106.11 (V-), U5107.11 (V-), U5108.11 (V-), U5109.11 (V-), U5110.11 (V-), U5111.11 (V-), U5112.11 (V-), U5113.11 (V-)
AC_BUFFER: U5111.6 (-), U5111.7, U5111.10 (+)
AC_NODE: C5108.2, C5109.2, C5110.2, C5111.2, C5112.2, C5113.2, C5114.2, C5115.2, C5116.2, C5117.2, R5166.1, U5111.5 (+)
AGND: C5101.2, C5102.2, C5103.2, C5104.2, C5119.2, C5120.2, C5121.2, C5122.2, C5123.2, C5124.2, C5125.2, C5126.2, C5127.2, C5128.2, C5129.2, C5130.2, C5131.2, C5132.2, C5133.2, C5134.2, C5135.2, C5136.2, C5137.2, C5138.2, C5139.2, C5140.2, C5141.2, C5142.2, C5143.2, D5104.1 (A), D5106.1 (K), D5107.2 (A), D5108.1 (K), D5109.2 (A), D5110.1 (K), D5111.2 (A), D5112.1 (K), D5113.2 (A), J907.S (Sleeve), J908.S (Sleeve), J1007.S (Sleeve), J1008.S (Sleeve), R5104.2, R5105.2, R5107.2, R5109.2, R5111.2, R5113.2, R5115.2, R5118.2, R5120.2, R5124.2, R5134.2, R5141.2, R5143.2, R5165.2, R5166.2, R5170.2, R5173.2, R5174.2, R5175.2, RV907.1 (CCW), RV1007.1 (CCW), RV1008.1 (CCW), U5101.4 (GND), U5102.5 (GND), U5102.6 (S4), U5102.7 (D4), U5102.8 (IN4), U5102.9 (IN3), U5102.10 (D3), U5102.11 (S3), U5102.14 (S2), U5102.15 (D2), U5102.16 (IN2), U5103.5 (GND), U5103.6 (S4), U5103.7 (D4), U5103.8 (IN4), U5103.9 (IN3), U5103.10 (D3), U5103.11 (S3), U5103.14 (S2), U5103.15 (D2), U5103.16 (IN2), U5104.5 (GND), U5104.6 (S4), U5104.7 (D4), U5104.8 (IN4), U5104.9 (IN3), U5104.10 (D3), U5104.11 (S3), U5104.14 (S2), U5104.15 (D2), U5104.16 (IN2), U5105.7, U5105.10, U5105.13 (-), U5105.14 (+), U5106.5 (+), U5106.12 (+), U5108.3 (+), U5108.5 (+), U5109.5 (+), U5109.10 (+), U5109.12 (+), U5113.12 (+)
BASE: D5105.2 (A), Q5101.1 (B), R5138.2
BASE_DRIVE: C5107.1, R5138.1, U5109.1
BIAS_BUFFER: R5148.1, U5112.8, U5112.9 (-), U5113.10 (+)
BIAS_MANUAL: R5147.1, U5107.6 (-), U5107.7
BIAS_PROTECTED: R5115.1, R5116.1, U5104.2 (D1)
BIAS_TIP: J908.T (Tip), U5104.3 (S1)
C01cf3e_DRIVE: C5118.1, R5167.1, U5111.8
C01cf3e_FB: C5118.2, R5168.2, U5111.9 (-)
C4c1698_W: R5119.1, RV908.2 (WIPER)
C4c1698_W_SENSE: C5104.1, R5119.2, R5120.1, U5107.5 (+)
C7cd0c4_ENABLE: R5105.1, R5106.2, U5102.1 (IN1)
C8df94f_SENSE: D5101.3 (COM), R5108.2, U5112.3 (+)
C9cfd7a_DRIVE: C5105.1, R5121.1, U5107.8
C9cfd7a_FB: C5105.2, R5122.2, U5107.9 (-)
C029db8_DRIVE: D5124.2 (A), D5126.1 (K), U5113.8
C029db8_LED_A: D908.2 (A), D5124.1 (K), D5125.1 (K)
C029db8_LED_K: D908.1 (K), D5126.2 (A), D5127.2 (A)
C029db8_SENSE: D5125.2 (A), D5127.1 (K), R5175.1, U5113.9 (-)
C73c7d0_GATE_RAW: R5103.2, R5104.1, U5106.10 (+)
C73c7d0_GATE_REF: U5106.8, U5106.9 (-)
C73c7d0_INV: R5101.2, R5102.2, U5106.6 (-)
C73c7d0_RAW_5V: C5102.1, U5101.6 (Vout), U5106.3 (+)
C74d1de_SENSE: D5102.3 (COM), R5112.2, U5112.5 (+)
C75db46_W: R5117.1, RV907.2 (WIPER)
C75db46_W_SENSE: C5103.1, R5117.2, R5118.1, U5107.3 (+)
C92bfbf_DRIVE: R5171.1, U5112.13 (-), U5112.14
C92bfbf_ISO_MID: R5171.2, R5172.1
C554ad0_SENSE: D5103.3 (COM), R5116.2, U5112.10 (+)
C768aa2_ENABLE: R5113.1, R5114.2, U5104.1 (IN1)
C20383d_DRIVE: D5114.2 (A), D5116.1 (K), U5113.1
C20383d_LED_A: D907.2 (A), D5114.1 (K), D5115.1 (K)
C20383d_LED_K: D907.1 (K), D5116.2 (A), D5117.2 (A)
C20383d_SENSE: D5115.2 (A), D5117.1 (K), R5173.1, U5113.2 (-)
C629978_W: R5169.1, RV1008.2 (WIPER)
C629978_W_SENSE: R5169.2, R5170.1, U5111.12 (+)
COMMAND: R5135.1, U5108.8, U5108.9 (-)
CONTROL_CLAMP: D5104.3 (COM), R5132.2, U5108.10 (+)
CONTROL_INV: R5130.2, R5131.2, U5108.6 (-)
CONTROL_NEG: R5129.1, R5130.1, U5108.1
CONTROL_RAW: R5131.1, R5132.1, U5108.7
CONTROL_SUM: R5127.2, R5128.2, R5129.2, U5108.2 (-)
CORE_PACK_OPA4197IPWR_0_IO_UNUSED4: U5106.13 (-), U5106.14
CURRENT_SOURCE: Q5101.3 (C), R5139.1
Cb36f8a_SUM: C5106.2, R5125.2, R5126.2, U5107.13 (-)
Cb36f8a_W: R5123.1, RV1007.2 (WIPER)
Cb36f8a_W_SENSE: R5123.2, R5124.1, U5107.12 (+)
Cb68133_DRIVE: D5119.2 (A), D5121.1 (K), U5113.7
Cb68133_LED_A: D1007.2 (A), D5119.1 (K), D5120.1 (K)
Cb68133_LED_K: D1007.1 (K), D5121.2 (A), D5122.2 (A)
Cb68133_SENSE: D5120.2 (A), D5122.1 (K), R5174.1, U5113.6 (-)
Cfda5dc_ENABLE: R5109.1, R5110.2, U5103.1 (IN1)
DRIVE_INV_SUM: R5150.2, R5151.2, U5109.13 (-)
EMITTER: C5107.2, D5105.1 (K), Q5101.2 (E), R5137.2, U5109.2 (-)
F1_CLIP: D5106.2 (A), D5107.1 (K), R5152.2, U5110.3 (+)
F1_OUT: R5154.1, R5155.1, R5156.1, U5110.1
F1_SUM: R5153.2, R5154.2, U5110.2 (-)
F2_CLIP: D5108.2 (A), D5109.1 (K), R5155.2, U5110.5 (+)
F2_OUT: R5157.1, R5158.1, R5159.1, U5110.7
F2_SUM: R5156.2, R5157.2, U5110.6 (-)
F3_CLIP: D5110.2 (A), D5111.1 (K), R5158.2, U5110.10 (+)
F3_OUT: R5160.1, R5161.1, R5162.1, U5110.8
F3_SUM: R5159.2, R5160.2, U5110.9 (-)
F4_CLIP: D5112.2 (A), D5113.1 (K), R5161.2, U5110.12 (+)
F4_OUT: R5163.1, U5110.14, U5111.3 (+)
F4_SUM: R5162.2, R5163.2, U5110.13 (-)
FOLDER_DRIVE: R5151.1, R5152.1, R5153.1, U5109.14
FOLDER_NEG: R5149.1, R5150.1, U5109.8
FOLDER_SUM: R5146.2, R5147.2, R5148.2, R5149.2, U5109.9 (-)
FOLD_BUFFER: R5125.1, U5107.10 (+), U5112.6 (-), U5112.7, U5113.5 (+)
FOLD_DEPTH: C5106.1, R5126.1, R5128.1, U5107.14
FOLD_MANUAL: R5127.1, U5107.1, U5107.2 (-)
FOLD_PROTECTED: R5111.1, R5112.1, U5103.2 (D1)
FOLD_REMOTE: R5121.2, R5122.1, RV1007.3 (CW)
FOLD_TIP: J1007.T (Tip), U5103.3 (S1)
IABC: R5139.2, U5105.1
IN_BUFFER: R5140.1, U5112.1, U5112.2 (-), U5113.3 (+)
IN_PROTECTED: R5107.1, R5108.1, U5102.2 (D1)
IN_TIP: J907.T (Tip), U5102.3 (S1)
LED_PACK_OPA4196IDR_0_IO_UNUSED4: U5113.13 (-), U5113.14
LEVEL_OUT: U5111.13 (-), U5111.14, U5112.12 (+)
LEVEL_REMOTE: R5167.2, R5168.1, RV1008.3 (CW)
OFFSET_TRIM: R5142.1, RV5104.2 (Wiper)
OTA_OFFSET: R5142.2, R5143.1, U5105.3 (+)
OTA_SIGNAL: R5140.2, R5141.1, U5105.4 (-)
OUTPUT_FB: R5164.2, R5165.1, U5111.2 (-)
OUT_TIP: J1008.T (Tip), R5172.2
PRE_AC: C5108.1, C5109.1, C5110.1, C5111.1, C5112.1, C5113.1, C5114.1, C5115.1, C5116.1, C5117.1, R5164.1, U5111.1
PRE_GAIN: R5145.1, R5146.1, U5109.7
PRE_GAIN_SUM: RV5105.2 (Wiper), RV5105.3 (CW), U5105.5, U5109.6 (-)
PRE_GAIN_TRIM: R5145.2, RV5105.1 (CCW)
REF5: D5104.2 (K), R5101.1, R5103.1, R5133.1, R5137.1, RV907.3 (CW), RV908.3 (CW), RV5104.3 (CW), U5106.1, U5106.2 (-)
REF25: R5133.2, R5134.1, U5108.12 (+)
REFN5: R5102.1, RV908.1 (CCW), RV5104.1 (CCW), U5106.7
TARGET: R5136.1, U5108.14, U5109.3 (+)
TARGET_SUM: R5135.2, R5136.2, U5108.13 (-)
UNUSED_IABC: R5144.1, U5105.16
