Takazudo/zudo-osc-hole-field/boards/osc-core/sheets/board_interfaces_K-p2.kicad_sch

## KiCad design boards/osc-core/sheets/board_interfaces_K-p2.kicad_sch (2026-09-30)

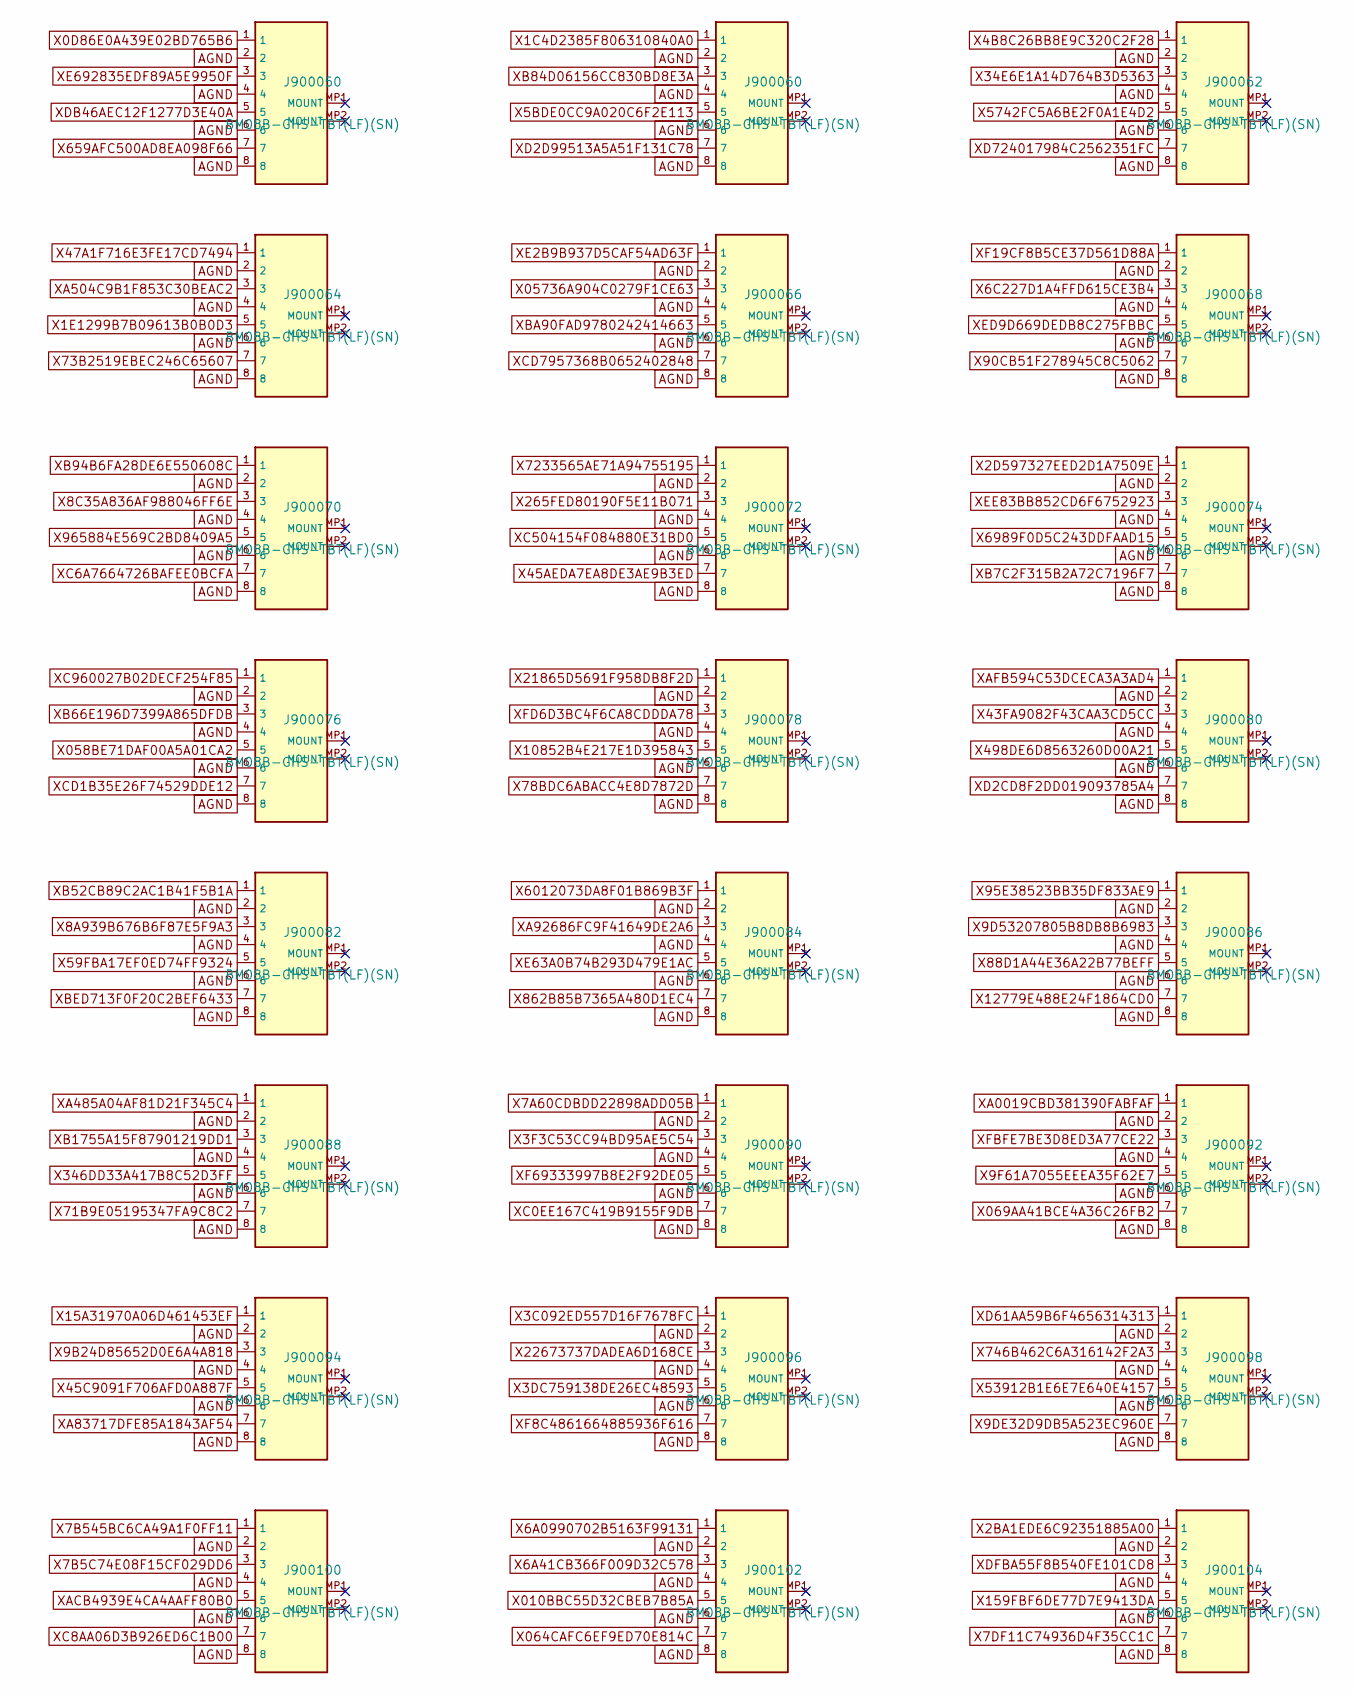
[picture p149: schematic board_interfaces_K-p2.kicad_sch]

Parts:
J900050, J900060, J900062, J900064, J900066, J900068, J900070, J900072, J900074, J900076, J900078, J900080, J900082, J900084, J900086, J900088, J900090, J900092, J900094, J900096, J900098, J900100, J900102, J900104: BM08B-GHS-TBT(LF)(SN); JST_GH8_BM_TopEntry; MPN BM08B-GHS-TBT(LF)(SN)

Connections:
AGND: J900050.2, J900050.4, J900050.6, J900050.8, J900060.2, J900060.4, J900060.6, J900060.8, J900062.2, J900062.4, J900062.6, J900062.8, J900064.2, J900064.4, J900064.6, J900064.8, J900066.2, J900066.4, J900066.6, J900066.8, J900068.2, J900068.4, J900068.6, J900068.8, J900070.2, J900070.4, J900070.6, J900070.8, J900072.2, J900072.4, J900072.6, J900072.8, J900074.2, J900074.4, J900074.6, J900074.8, J900076.2, J900076.4, J900076.6, J900076.8, J900078.2, J900078.4, J900078.6, J900078.8, J900080.2, J900080.4, J900080.6, J900080.8, J900082.2, J900082.4, J900082.6, J900082.8, J900084.2, J900084.4, J900084.6, J900084.8, J900086.2, J900086.4, J900086.6, J900086.8, J900088.2, J900088.4, J900088.6, J900088.8, J900090.2, J900090.4, J900090.6, J900090.8, J900092.2, J900092.4, J900092.6, J900092.8, J900094.2, J900094.4, J900094.6, J900094.8, J900096.2, J900096.4, J900096.6, J900096.8, J900098.2, J900098.4, J900098.6, J900098.8, J900100.2, J900100.4, J900100.6, J900100.8, J900102.2, J900102.4, J900102.6, J900102.8, J900104.2, J900104.4, J900104.6, J900104.8
X0D86E0A439E02BD765B6: J900050.1
X1C4D2385F806310840A0: J900060.1
X1E1299B7B09613B0B0D3: J900064.5
X2BA1EDE6C92351885A00: J900104.1
X2D597327EED2D1A7509E: J900074.1
X3C092ED557D16F7678FC: J900096.1
X3DC759138DE26EC48593: J900096.5
X3F3C53CC94BD95AE5C54: J900090.3
X4B8C26BB8E9C320C2F28: J900062.1
X5BDE0CC9A020C6F2E113: J900060.5
X6A41CB366F009D32C578: J900102.3
X6A0990702B5163F99131: J900102.1
X6C227D1A4FFD615CE3B4: J900068.3
X7A60CDBDD22898ADD05B: J900090.1
X7B5C74E08F15CF029DD6: J900100.3
X7B545BC6CA49A1F0FF11: J900100.1
X7DF11C74936D4F35CC1C: J900104.7
X8A939B676B6F87E5F9A3: J900082.3
X8C35A836AF988046FF6E: J900070.3
X9B24D85652D0E6A4A818: J900094.3
X9D53207805B8DB8B6983: J900086.3
X9DE32D9DB5A523EC960E: J900098.7
X9F61A7055EEEA35F62E7: J900092.5
X010BBC55D32CBEB7B85A: J900102.5
X15A31970A06D461453EF: J900094.1
X34E6E1A14D764B3D5363: J900062.3
X43FA9082F43CAA3CD5CC: J900080.3
X45AEDA7EA8DE3AE9B3ED: J900072.7
X45C9091F706AFD0A887F: J900094.5
X47A1F716E3FE17CD7494: J900064.1
X058BE71DAF00A5A01CA2: J900076.5
X59FBA17EF0ED74FF9324: J900082.5
X064CAFC6EF9ED70E814C: J900102.7
X069AA41BCE4A36C26FB2: J900092.7
X71B9E05195347FA9C8C2: J900088.7
X73B2519EBEC246C65607: J900064.7
X78BDC6ABACC4E8D7872D: J900078.7
X88D1A44E36A22B77BEFF: J900086.5
X90CB51F278945C8C5062: J900068.7
X95E38523BB35DF833AE9: J900086.1
X159FBF6DE77D7E9413DA: J900104.5
X265FED80190F5E11B071: J900072.3
X346DD33A417B8C52D3FF: J900088.5
X498DE6D8563260D00A21: J900080.5
X659AFC500AD8EA098F66: J900050.7
X746B462C6A316142F2A3: J900098.3
X862B85B7365A480D1EC4: J900084.7
X05736A904C0279F1CE63: J900066.3
X5742FC5A6BE2F0A1E4D2: J900062.5
X6989F0D5C243DDFAAD15: J900074.5
X10852B4E217E1D395843: J900078.5
X12779E488E24F1864CD0: J900086.7
X21865D5691F958DB8F2D: J900078.1
X53912B1E6E7E640E4157: J900098.5
X965884E569C2BD8409A5: J900070.5
X6012073DA8F01B869B3F: J900084.1
X7233565AE71A94755195: J900072.1
X22673737DADEA6D168CE: J900096.3
XA0019CBD381390FABFAF: J900092.1
XA485A04AF81D21F345C4: J900088.1
XA504C9B1F853C30BEAC2: J900064.3
XA83717DFE85A1843AF54: J900094.7
XA92686FC9F41649DE2A6: J900084.3
XACB4939E4CA4AAFF80B0: J900100.5
XAFB594C53DCECA3A3AD4: J900080.1
XB7C2F315B2A72C7196F7: J900074.7
XB52CB89C2AC1B41F5B1A: J900082.1
XB66E196D7399A865DFDB: J900076.3
XB84D06156CC830BD8E3A: J900060.3
XB94B6FA28DE6E550608C: J900070.1
XB1755A15F87901219DD1: J900088.3
XBA90FAD9780242414663: J900066.5
XBED713F0F20C2BEF6433: J900082.7
XC0EE167C419B9155F9DB: J900090.7
XC6A7664726BAFEE0BCFA: J900070.7
XC8AA06D3B926ED6C1B00: J900100.7
XC504154F084880E31BD0: J900072.5
XC960027B02DECF254F85: J900076.1
XCD1B35E26F74529DDE12: J900076.7
XCD7957368B0652402848: J900066.7
XD2CD8F2DD019093785A4: J900080.7
XD2D99513A5A51F131C78: J900060.7
XD61AA59B6F4656314313: J900098.1
XD724017984C2562351FC: J900062.7
XDB46AEC12F1277D3E40A: J900050.5
XDFBA55F8B540FE101CD8: J900104.3
XE2B9B937D5CAF54AD63F: J900066.1
XE63A0B74B293D479E1AC: J900084.5
XE692835EDF89A5E9950F: J900050.3
XED9D669DEDB8C275FBBC: J900068.5
XEE83BB852CD6F6752923: J900074.3
XF8C4861664885936F616: J900096.7
XF19CF8B5CE37D561D88A: J900068.1
XF69333997B8E2F92DE05: J900090.5
XFBFE7BE3D8ED3A77CE22: J900092.3
XFD6D3BC4F6CA8CDDDA78: J900078.3
