Takazudo/zudo-osc-hole-field/boards/osc-core/sheets/board_interfaces_K-p3.kicad_sch

## KiCad design boards/osc-core/sheets/board_interfaces_K-p3.kicad_sch (2026-10-02)

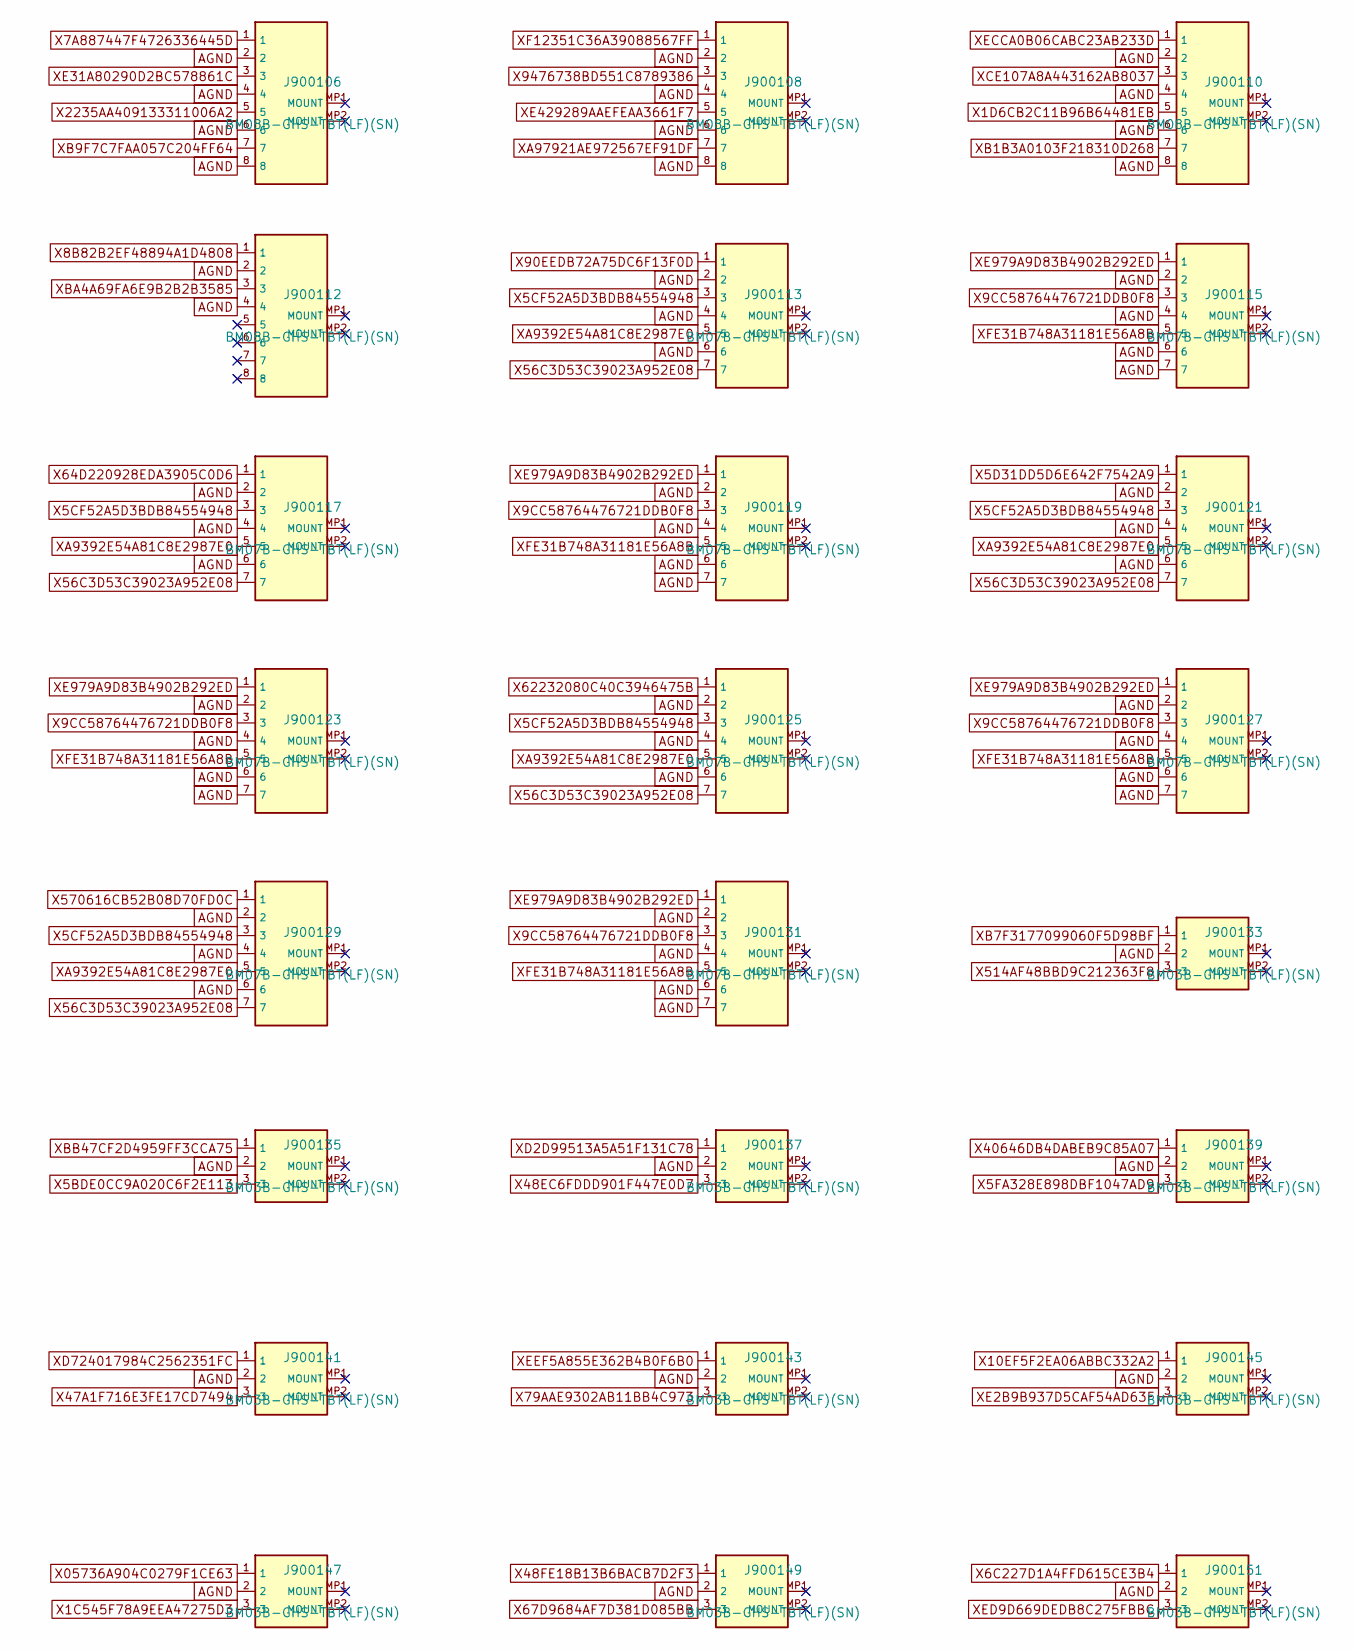
[picture p150: schematic board_interfaces_K-p3.kicad_sch]

Parts:
J900106, J900108, J900110, J900112: BM08B-GHS-TBT(LF)(SN); JST_GH8_BM_TopEntry; MPN BM08B-GHS-TBT(LF)(SN)
J900113, J900115, J900117, J900119, J900121, J900123, J900125, J900127, J900129, J900131: BM07B-GHS-TBT(LF)(SN); JST_GH7_BM_TopEntry; MPN BM07B-GHS-TBT(LF)(SN)
J900133, J900135, J900137, J900139, J900141, J900143, J900145, J900147, J900149, J900151: BM03B-GHS-TBT(LF)(SN); JST_GH3_BM_TopEntry; MPN BM03B-GHS-TBT(LF)(SN)

Connections:
AGND: J900106.2, J900106.4, J900106.6, J900106.8, J900108.2, J900108.4, J900108.6, J900108.8, J900110.2, J900110.4, J900110.6, J900110.8, J900112.2, J900112.4, J900113.2, J900113.4, J900113.6, J900115.2, J900115.4, J900115.6, J900115.7, J900117.2, J900117.4, J900117.6, J900119.2, J900119.4, J900119.6, J900119.7, J900121.2, J900121.4, J900121.6, J900123.2, J900123.4, J900123.6, J900123.7, J900125.2, J900125.4, J900125.6, J900127.2, J900127.4, J900127.6, J900127.7, J900129.2, J900129.4, J900129.6, J900131.2, J900131.4, J900131.6, J900131.7, J900133.2, J900135.2, J900137.2, J900139.2, J900141.2, J900143.2, J900145.2, J900147.2, J900149.2, J900151.2
X1C545F78A9EEA47275D3: J900147.3
X1D6CB2C11B96B64481EB: J900110.5
X5BDE0CC9A020C6F2E113: J900135.3
X5CF52A5D3BDB84554948: J900113.3, J900117.3, J900121.3, J900125.3, J900129.3
X5D31DD5D6E642F7542A9: J900121.1
X5FA328E898DBF1047AD9: J900139.3
X6C227D1A4FFD615CE3B4: J900151.1
X7A887447F4726336445D: J900106.1
X8B82B2EF48894A1D4808: J900112.1
X9CC58764476721DDB0F8: J900115.3, J900119.3, J900123.3, J900127.3, J900131.3
X10EF5F2EA06ABBC332A2: J900145.1
X47A1F716E3FE17CD7494: J900141.3
X48EC6FDDD901F447E0D7: J900137.3
X48FE18B13B6BACB7D2F3: J900149.1
X56C3D53C39023A952E08: J900113.7, J900117.7, J900121.7, J900125.7, J900129.7
X64D220928EDA3905C0D6: J900117.1
X67D9684AF7D381D085BB: J900149.3
X79AAE9302AB11BB4C973: J900143.3
X90EEDB72A75DC6F13F0D: J900113.1
X514AF48BBD9C212363F8: J900133.3
X2235AA409133311006A2: J900106.5
X05736A904C0279F1CE63: J900147.1
X40646DB4DABEB9C85A07: J900139.1
X570616CB52B08D70FD0C: J900129.1
X9476738BD551C8789386: J900108.3
X62232080C40C3946475B: J900125.1
XA9392E54A81C8E2987E0: J900113.5, J900117.5, J900121.5, J900125.5, J900129.5
XA97921AE972567EF91DF: J900108.7
XB1B3A0103F218310D268: J900110.7
XB7F3177099060F5D98BF: J900133.1
XB9F7C7FAA057C204FF64: J900106.7
XBA4A69FA6E9B2B2B3585: J900112.3
XBB47CF2D4959FF3CCA75: J900135.1
XCE107A8A443162AB8037: J900110.3
XD2D99513A5A51F131C78: J900137.1
XD724017984C2562351FC: J900141.1
XE2B9B937D5CAF54AD63F: J900145.3
XE31A80290D2BC578861C: J900106.3
XE979A9D83B4902B292ED: J900115.1, J900119.1, J900123.1, J900127.1, J900131.1
XE429289AAEFEAA3661F7: J900108.5
XECCA0B06CABC23AB233D: J900110.1
XED9D669DEDB8C275FBBC: J900151.3
XEEF5A855E362B4B0F6B0: J900143.1
XF12351C36A39088567FF: J900108.1
XFE31B748A31181E56A8B: J900115.5, J900119.5, J900123.5, J900127.5, J900131.5
