Takazudo/zudo-osc-hole-field/boards/osc-core/sheets/board_interfaces_K-p4.kicad_sch

## KiCad design boards/osc-core/sheets/board_interfaces_K-p4.kicad_sch (2026-10-02)

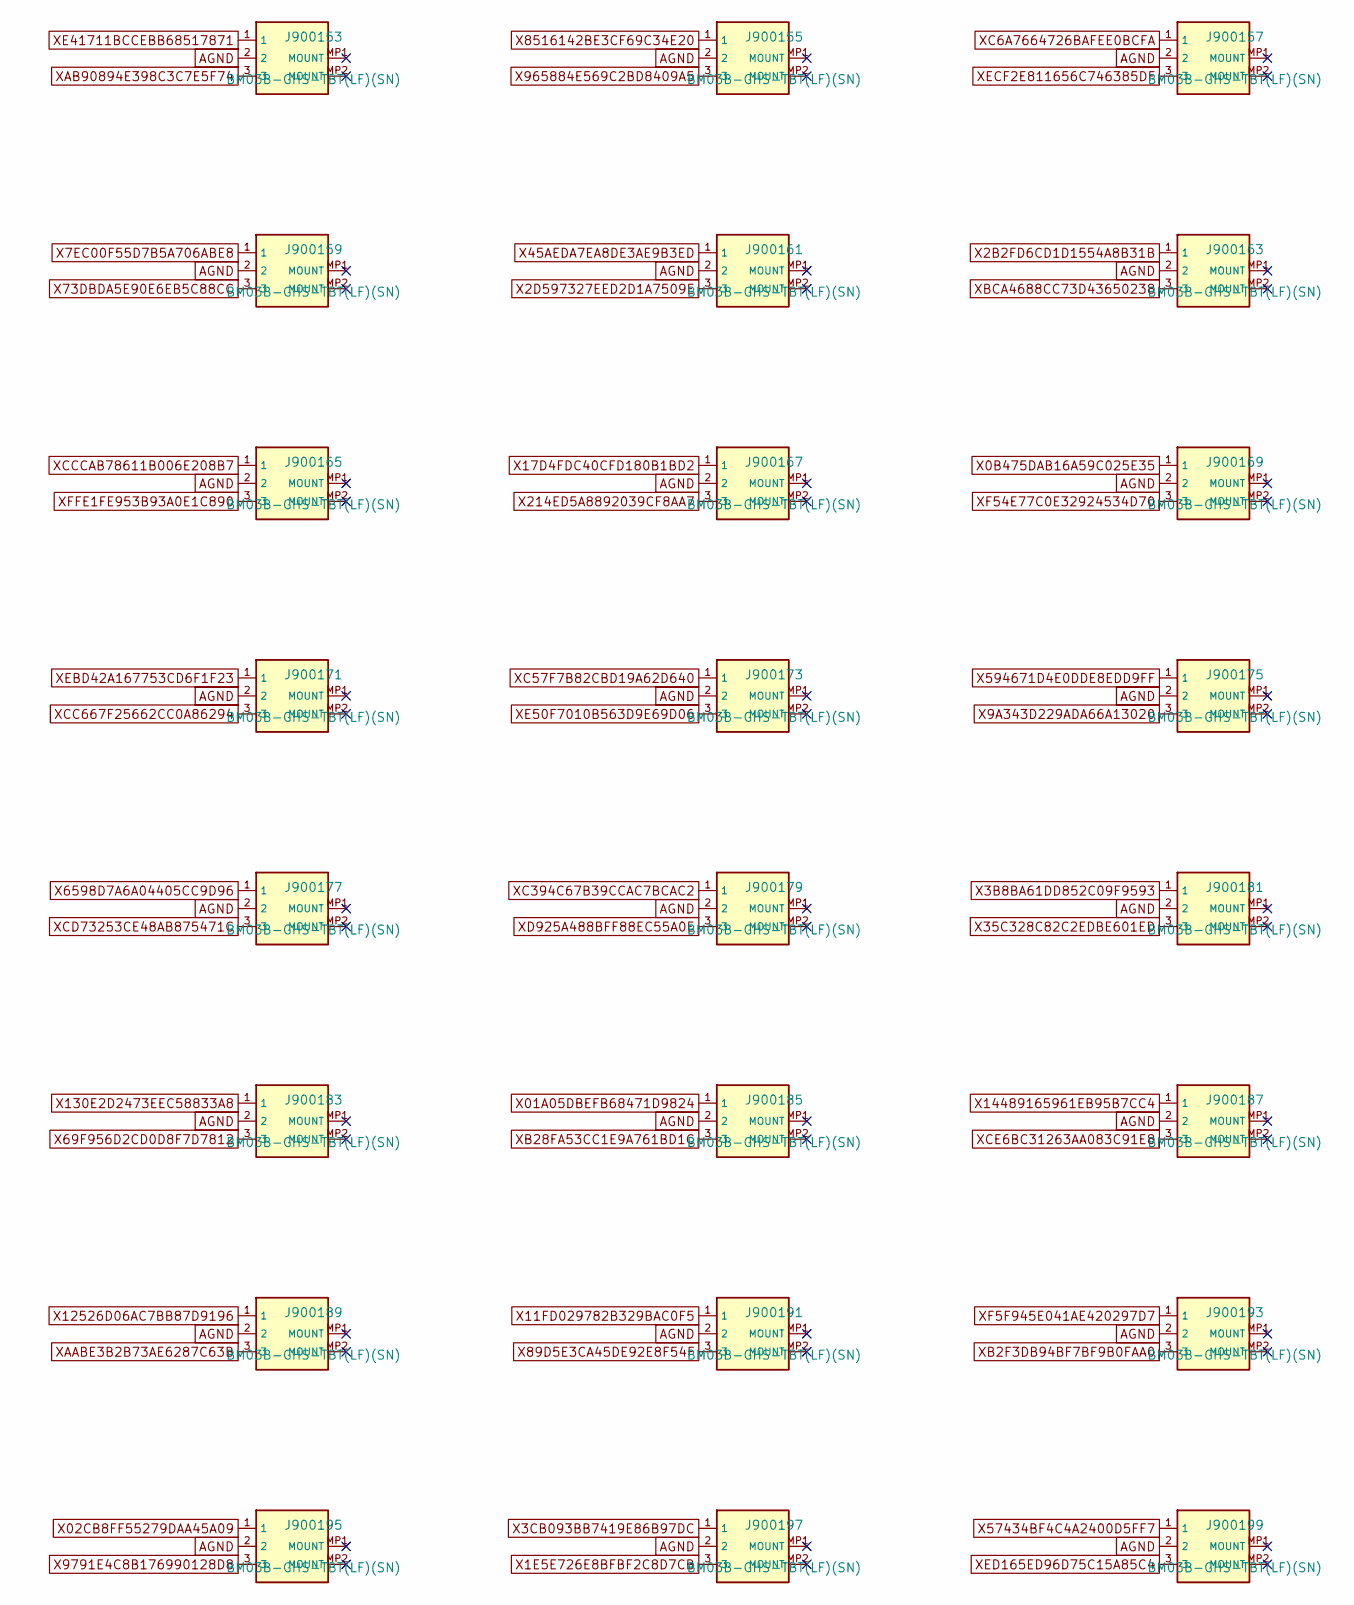
[picture p151: schematic board_interfaces_K-p4.kicad_sch]

Parts:
J900153, J900155, J900157, J900159, J900161, J900163, J900165, J900167, J900169, J900171, J900173, J900175, J900177, J900179, J900181, J900183, J900185, J900187, J900189, J900191, J900193, J900195, J900197, J900199: BM03B-GHS-TBT(LF)(SN); JST_GH3_BM_TopEntry; MPN BM03B-GHS-TBT(LF)(SN)

Connections:
AGND: J900153.2, J900155.2, J900157.2, J900159.2, J900161.2, J900163.2, J900165.2, J900167.2, J900169.2, J900171.2, J900173.2, J900175.2, J900177.2, J900179.2, J900181.2, J900183.2, J900185.2, J900187.2, J900189.2, J900191.2, J900193.2, J900195.2, J900197.2, J900199.2
X0B475DAB16A59C025E35: J900169.1
X01A05DBEFB68471D9824: J900185.1
X1E5E726E8BFBF2C8D7CB: J900197.3
X2B2FD6CD1D1554A8B31B: J900163.1
X02CB8FF55279DAA45A09: J900195.1
X2D597327EED2D1A7509E: J900161.3
X3B8BA61DD852C09F9593: J900181.1
X3CB093BB7419E86B97DC: J900197.1
X7EC00F55D7B5A706ABE8: J900159.1
X9A343D229ADA66A13020: J900175.3
X11FD029782B329BAC0F5: J900191.1
X17D4FDC40CFD180B1BD2: J900167.1
X35C328C82C2EDBE601ED: J900181.3
X45AEDA7EA8DE3AE9B3ED: J900161.1
X69F956D2CD0D8F7D7812: J900183.3
X73DBDA5E90E6EB5C88CC: J900159.3
X89D5E3CA45DE92E8F54F: J900191.3
X130E2D2473EEC58833A8: J900183.1
X214ED5A8892039CF8AA7: J900167.3
X6598D7A6A04405CC9D96: J900177.1
X9791E4C8B176990128D8: J900195.3
X12526D06AC7BB87D9196: J900189.1
X57434BF4C4A2400D5FF7: J900199.1
X594671D4E0DDE8EDD9FF: J900175.1
X965884E569C2BD8409A5: J900155.3
X8516142BE3CF69C34E20: J900155.1
X14489165961EB95B7CC4: J900187.1
XAABE3B2B73AE6287C63B: J900189.3
XAB90894E398C3C7E5F74: J900153.3
XB2F3DB94BF7BF9B0FAA0: J900193.3
XB28FA53CC1E9A761BD1C: J900185.3
XBCA4688CC73D43650238: J900163.3
XC6A7664726BAFEE0BCFA: J900157.1
XC57F7B82CBD19A62D640: J900173.1
XC394C67B39CCAC7BCAC2: J900179.1
XCC667F25662CC0A86294: J900171.3
XCCCAB78611B006E208B7: J900165.1
XCD73253CE48AB875471C: J900177.3
XCE6BC31263AA083C91E8: J900187.3
XD925A488BFF88EC55A0E: J900179.3
XE50F7010B563D9E69D06: J900173.3
XE41711BCCEBB68517871: J900153.1
XEBD42A167753CD6F1F23: J900171.1
XECF2E811656C746385DF: J900157.3
XED165ED96D75C15A85C4: J900199.3
XF5F945E041AE420297D7: J900193.1
XF54E77C0E32924534D70: J900169.3
XFFE1FE953B93A0E1C890: J900165.3
