Takazudo/zudo-osc-hole-field/boards/osc-core/sheets/board_interfaces_K-p5.kicad_sch

## KiCad design boards/osc-core/sheets/board_interfaces_K-p5.kicad_sch (2026-10-02)

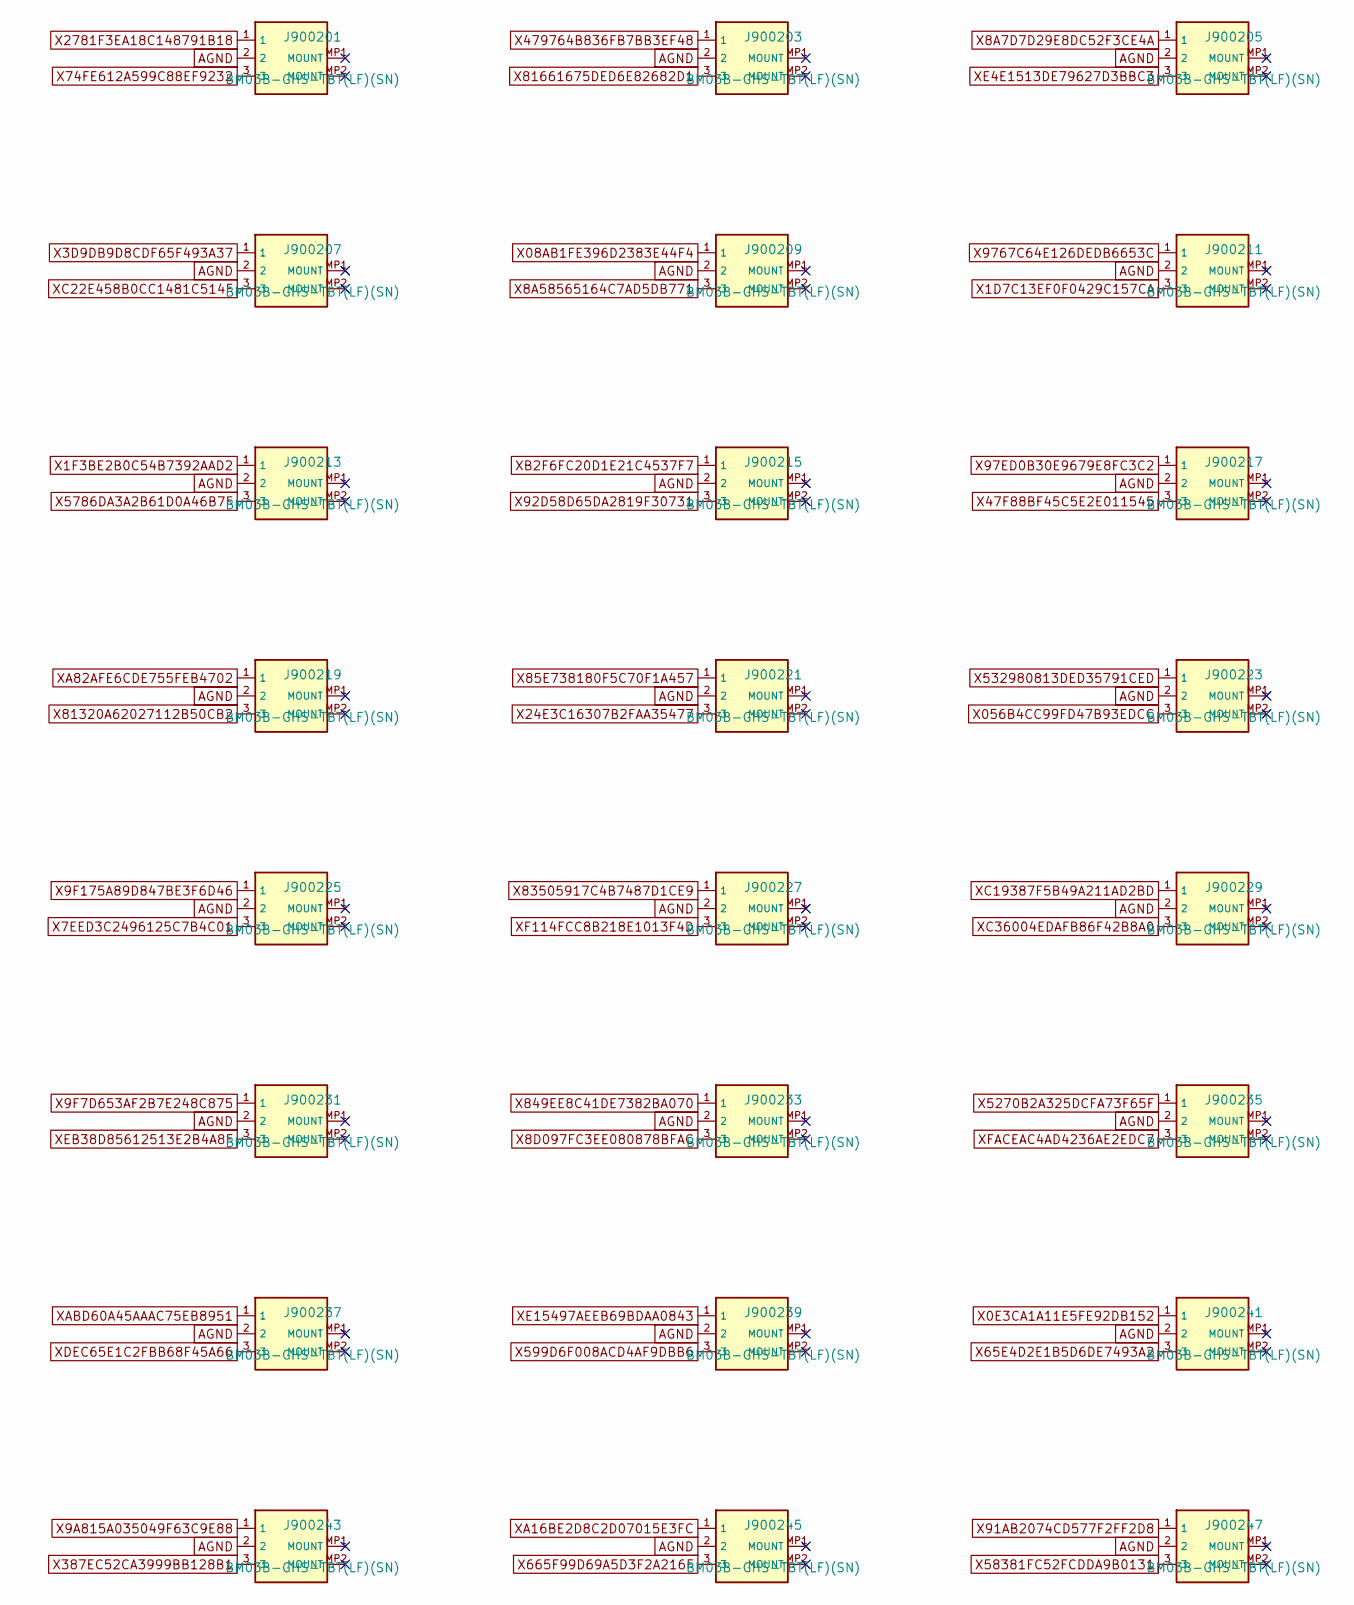
[picture p152: schematic board_interfaces_K-p5.kicad_sch]

Parts:
J900201, J900203, J900205, J900207, J900209, J900211, J900213, J900215, J900217, J900219, J900221, J900223, J900225, J900227, J900229, J900231, J900233, J900235, J900237, J900239, J900241, J900243, J900245, J900247: BM03B-GHS-TBT(LF)(SN); JST_GH3_BM_TopEntry; MPN BM03B-GHS-TBT(LF)(SN)

Connections:
AGND: J900201.2, J900203.2, J900205.2, J900207.2, J900209.2, J900211.2, J900213.2, J900215.2, J900217.2, J900219.2, J900221.2, J900223.2, J900225.2, J900227.2, J900229.2, J900231.2, J900233.2, J900235.2, J900237.2, J900239.2, J900241.2, J900243.2, J900245.2, J900247.2
X0E3CA1A11E5FE92DB152: J900241.1
X1D7C13EF0F0429C157CA: J900211.3
X1F3BE2B0C54B7392AAD2: J900213.1
X3D9DB9D8CDF65F493A37: J900207.1
X7EED3C2496125C7B4C01: J900225.3
X8A7D7D29E8DC52F3CE4A: J900205.1
X8A58565164C7AD5DB771: J900209.3
X08AB1FE396D2383E44F4: J900209.1
X8D097FC3EE080878BFAC: J900233.3
X9A815A035049F63C9E88: J900243.1
X9F7D653AF2B7E248C875: J900231.1
X9F175A89D847BE3F6D46: J900225.1
X24E3C16307B2FAA35477: J900221.3
X47F88BF45C5E2E011545: J900217.3
X056B4CC99FD47B93EDCC: J900223.3
X65E4D2E1B5D6DE7493A2: J900241.3
X74FE612A599C88EF9232: J900201.3
X85E738180F5C70F1A457: J900221.1
X91AB2074CD577F2FF2D8: J900247.1
X92D58D65DA2819F30731: J900215.3
X97ED0B30E9679E8FC3C2: J900217.1
X387EC52CA3999BB128B1: J900243.3
X599D6F008ACD4AF9DBB6: J900239.3
X665F99D69A5D3F2A216F: J900245.3
X849EE8C41DE7382BA070: J900233.1
X2781F3EA18C148791B18: J900201.1
X5270B2A325DCFA73F65F: J900235.1
X5786DA3A2B61D0A46B7F: J900213.3
X9767C64E126DEDB6653C: J900211.1
X58381FC52FCDDA9B0131: J900247.3
X81320A62027112B50CB2: J900219.3
X479764B836FB7BB3EF48: J900203.1
X81661675DED6E82682D1: J900203.3
X83505917C4B7487D1CE9: J900227.1
X532980813DED35791CED: J900223.1
XA16BE2D8C2D07015E3FC: J900245.1
XA82AFE6CDE755FEB4702: J900219.1
XABD60A45AAAC75EB8951: J900237.1
XB2F6FC20D1E21C4537F7: J900215.1
XC22E458B0CC1481C514F: J900207.3
XC19387F5B49A211AD2BD: J900229.1
XC36004EDAFB86F42B8A0: J900229.3
XDEC65E1C2FBB68F45A66: J900237.3
XE4E1513DE79627D3BBC3: J900205.3
XE15497AEEB69BDAA0843: J900239.1
XEB38D85612513E2B4A8F: J900231.3
XF114FCC8B218E1013F4D: J900227.3
XFACEAC4AD4236AE2EDC7: J900235.3
