Takazudo/zudo-osc-hole-field/boards/osc-core/sheets/board_interfaces_K-p6.kicad_sch

## KiCad design boards/osc-core/sheets/board_interfaces_K-p6.kicad_sch (2026-10-02)

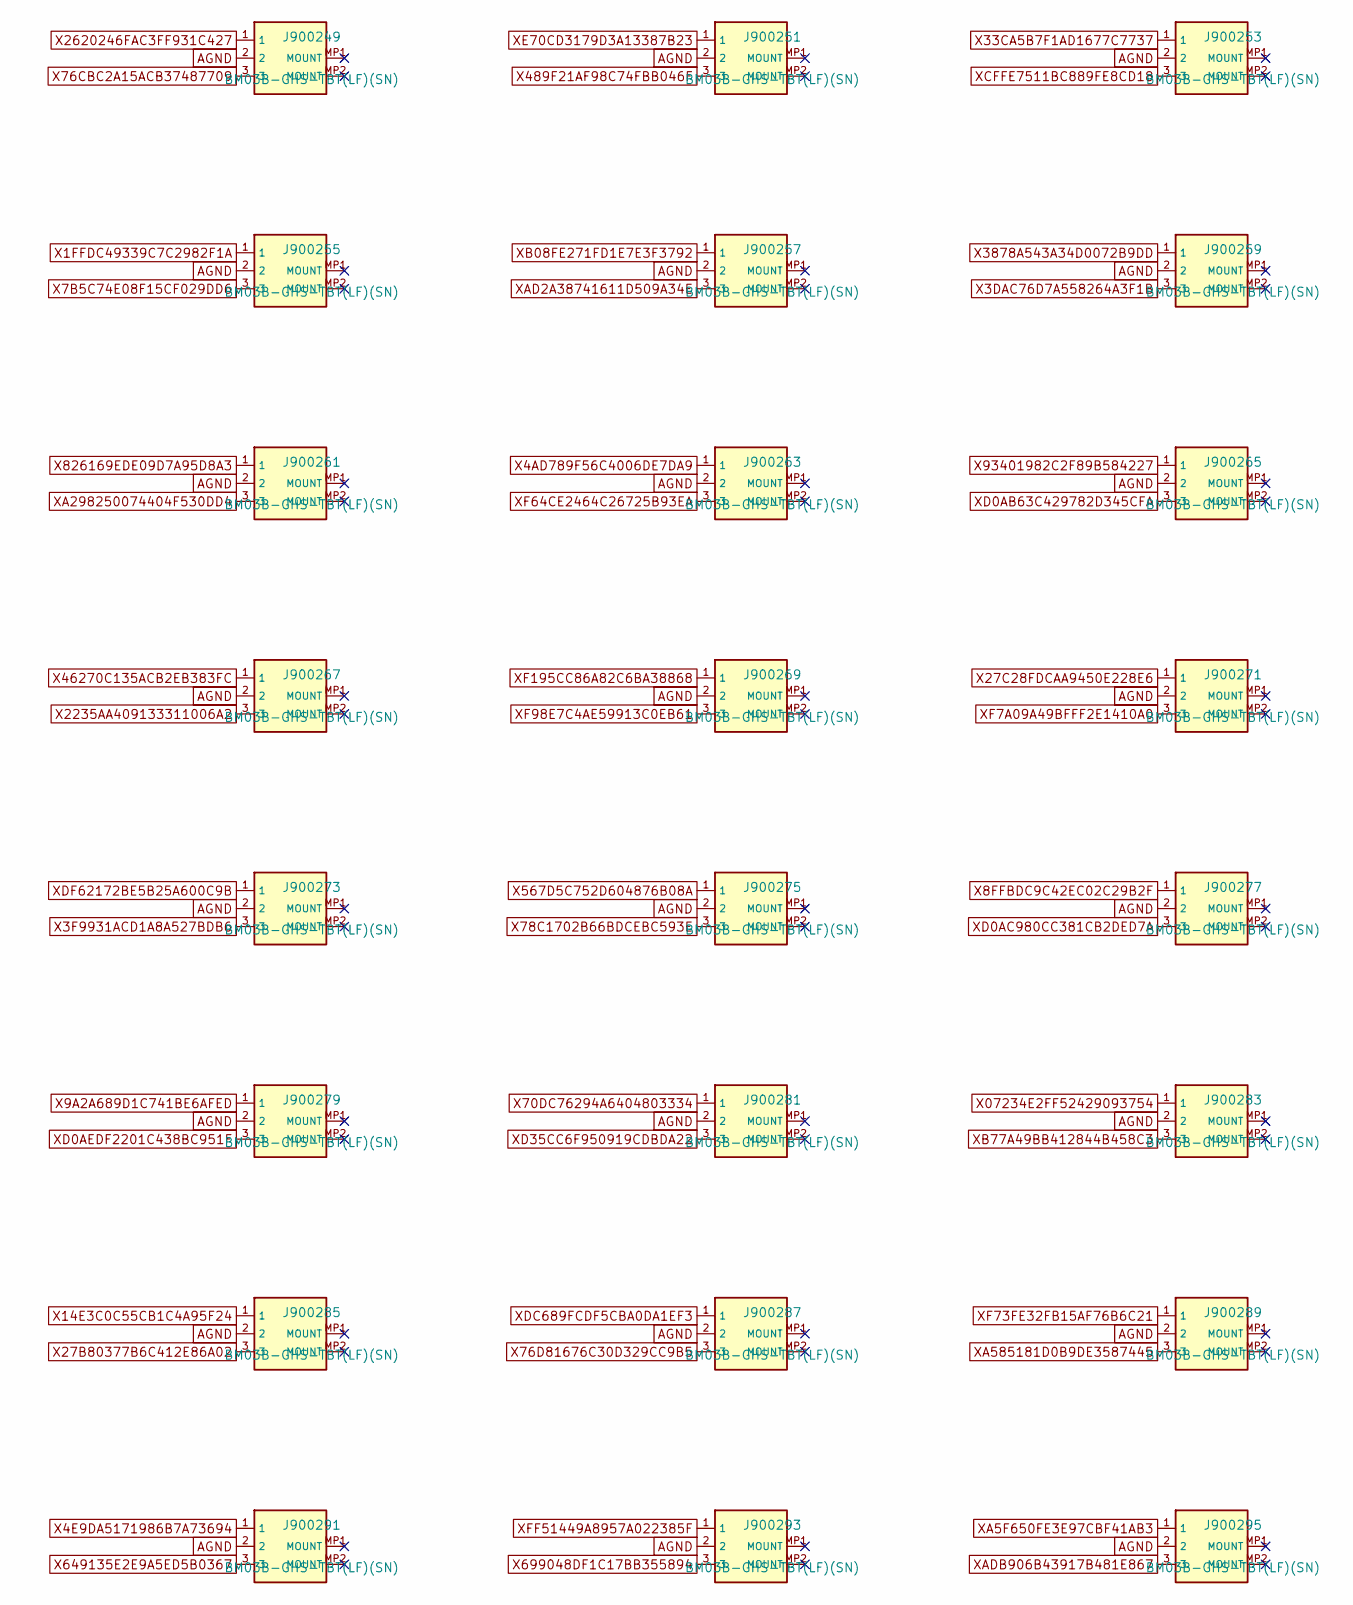
[picture p153: schematic board_interfaces_K-p6.kicad_sch]

Parts:
J900249, J900251, J900253, J900255, J900257, J900259, J900261, J900263, J900265, J900267, J900269, J900271, J900273, J900275, J900277, J900279, J900281, J900283, J900285, J900287, J900289, J900291, J900293, J900295: BM03B-GHS-TBT(LF)(SN); JST_GH3_BM_TopEntry; MPN BM03B-GHS-TBT(LF)(SN)

Connections:
AGND: J900249.2, J900251.2, J900253.2, J900255.2, J900257.2, J900259.2, J900261.2, J900263.2, J900265.2, J900267.2, J900269.2, J900271.2, J900273.2, J900275.2, J900277.2, J900279.2, J900281.2, J900283.2, J900285.2, J900287.2, J900289.2, J900291.2, J900293.2, J900295.2
X1FFDC49339C7C2982F1A: J900255.1
X3DAC76D7A558264A3F1B: J900259.3
X3F9931ACD1A8A527BDB6: J900273.3
X4AD789F56C4006DE7DA9: J900263.1
X4E9DA5171986B7A73694: J900291.1
X7B5C74E08F15CF029DD6: J900255.3
X8FFBDC9C42EC02C29B2F: J900277.1
X9A2A689D1C741BE6AFED: J900279.1
X14E3C0C55CB1C4A95F24: J900285.1
X27B80377B6C412E86A02: J900285.3
X27C28FDCAA9450E228E6: J900271.1
X33CA5B7F1AD1677C7737: J900253.1
X70DC76294A6404803334: J900281.1
X76CBC2A15ACB37487709: J900249.3
X76D81676C30D329CC9B5: J900287.3
X78C1702B66BDCEBC593E: J900275.3
X489F21AF98C74FBB046F: J900251.3
X567D5C752D604876B08A: J900275.1
X2235AA409133311006A2: J900267.3
X3878A543A34D0072B9DD: J900259.1
X07234E2FF52429093754: J900283.1
X46270C135ACB2EB383FC: J900267.1
X649135E2E9A5ED5B0367: J900291.3
X699048DF1C17BB355894: J900293.3
X826169EDE09D7A95D8A3: J900261.1
X2620246FAC3FF931C427: J900249.1
X93401982C2F89B584227: J900265.1
XA5F650FE3E97CBF41AB3: J900295.1
XA585181D0B9DE3587445: J900289.3
XA298250074404F530DD4: J900261.3
XAD2A38741611D509A34E: J900257.3
XADB906B43917B481E867: J900295.3
XB08FE271FD1E7E3F3792: J900257.1
XB77A49BB412844B458C3: J900283.3
XCFFE7511BC889FE8CD18: J900253.3
XD0AB63C429782D345CFA: J900265.3
XD0AC980CC381CB2DED7A: J900277.3
XD0AEDF2201C438BC951F: J900279.3
XD35CC6F950919CDBDA22: J900281.3
XDC689FCDF5CBA0DA1EF3: J900287.1
XDF62172BE5B25A600C9B: J900273.1
XE70CD3179D3A13387B23: J900251.1
XF7A09A49BFFF2E1410A0: J900271.3
XF64CE2464C26725B93EA: J900263.3
XF73FE32FB15AF76B6C21: J900289.1
XF98E7C4AE59913C0EB61: J900269.3
XF195CC86A82C6BA38868: J900269.1
XFF51449A8957A022385F: J900293.1
