Takazudo/zudo-osc-hole-field/boards/osc-core/sheets/board_interfaces_K-p7.kicad_sch

## KiCad design boards/osc-core/sheets/board_interfaces_K-p7.kicad_sch (2026-10-02)

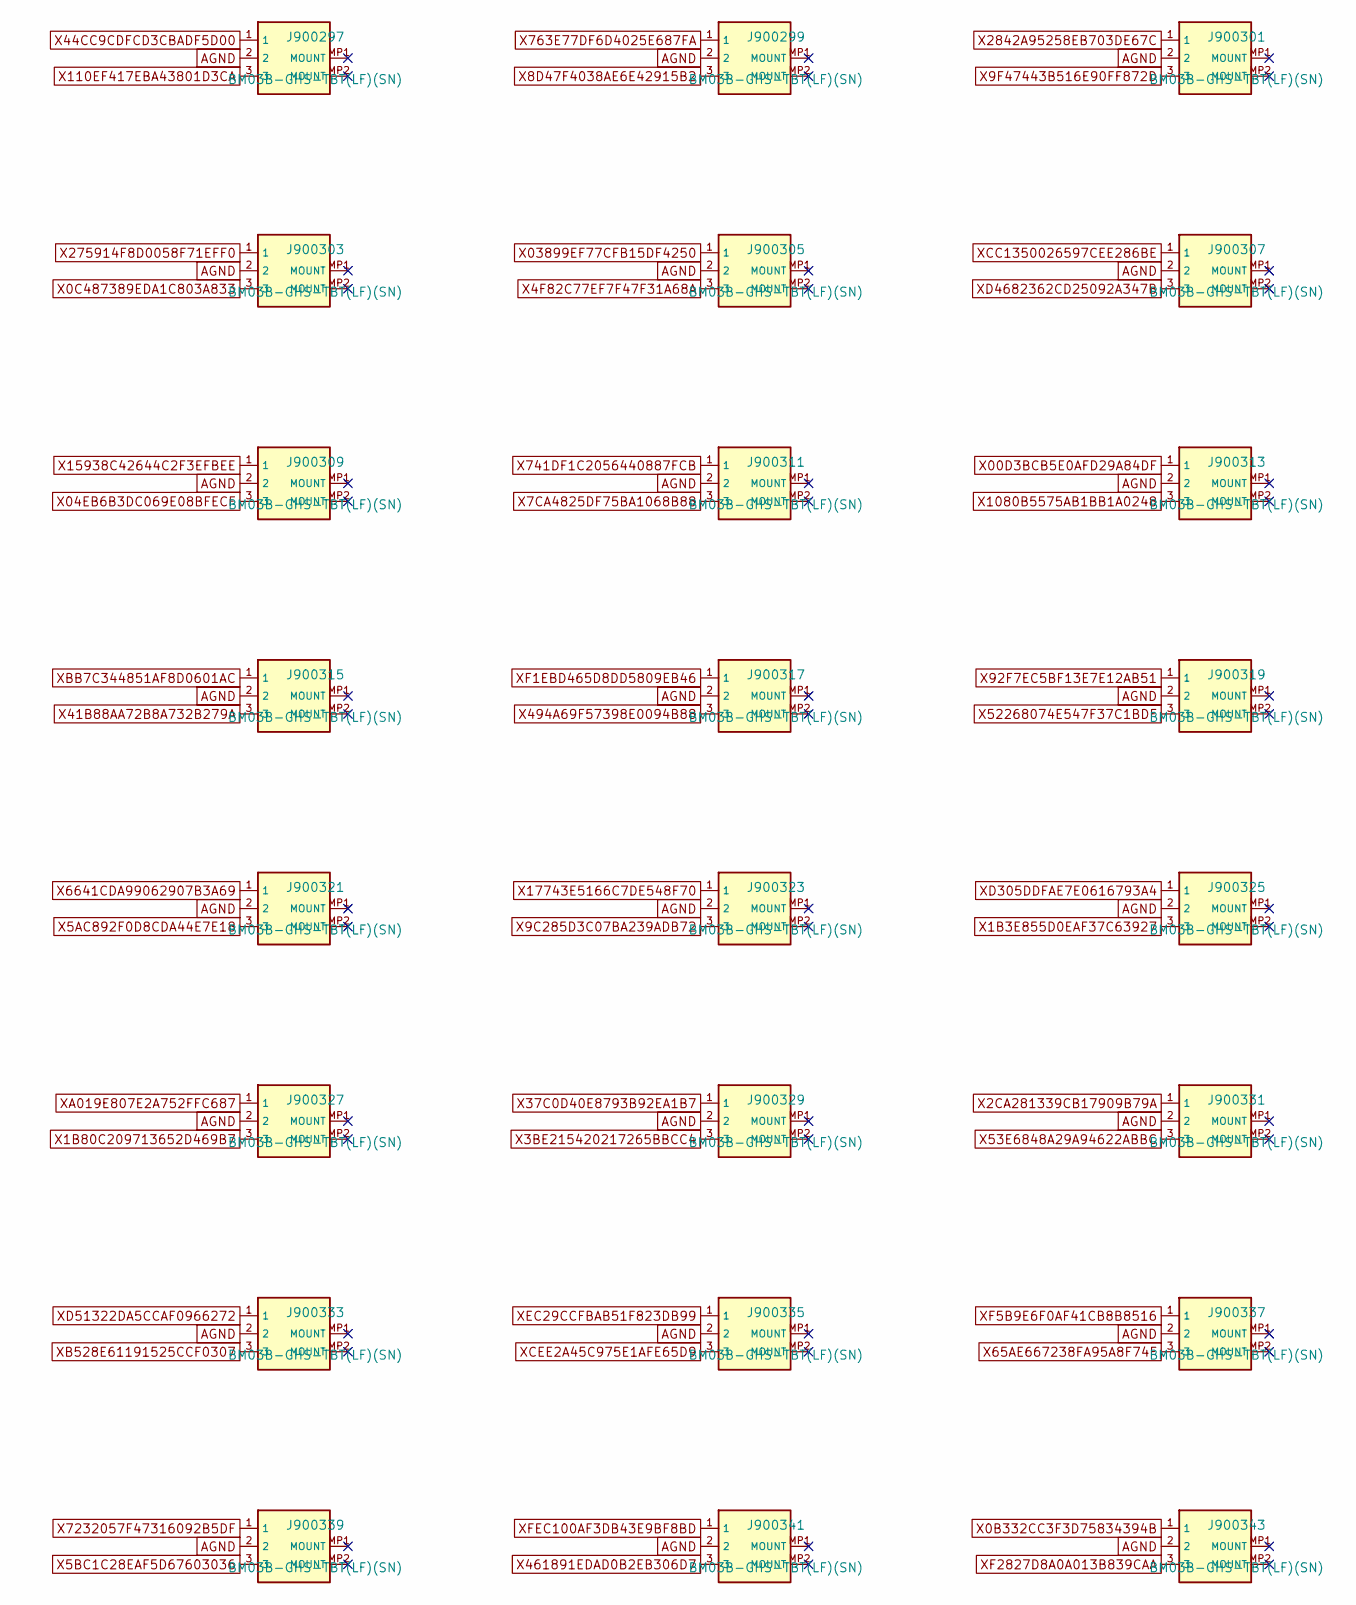
[picture p154: schematic board_interfaces_K-p7.kicad_sch]

Parts:
J900297, J900299, J900301, J900303, J900305, J900307, J900309, J900311, J900313, J900315, J900317, J900319, J900321, J900323, J900325, J900327, J900329, J900331, J900333, J900335, J900337, J900339, J900341, J900343: BM03B-GHS-TBT(LF)(SN); JST_GH3_BM_TopEntry; MPN BM03B-GHS-TBT(LF)(SN)

Connections:
AGND: J900297.2, J900299.2, J900301.2, J900303.2, J900305.2, J900307.2, J900309.2, J900311.2, J900313.2, J900315.2, J900317.2, J900319.2, J900321.2, J900323.2, J900325.2, J900327.2, J900329.2, J900331.2, J900333.2, J900335.2, J900337.2, J900339.2, J900341.2, J900343.2
X0B332CC3F3D75834394B: J900343.1
X0C487389EDA1C803A833: J900303.3
X00D3BCB5E0AFD29A84DF: J900313.1
X1B3E855D0EAF37C63927: J900325.3
X1B80C209713652D469B7: J900327.3
X2CA281339CB17909B79A: J900331.1
X3BE215420217265BBCC4: J900329.3
X04EB6B3DC069E08BFECF: J900309.3
X4F82C77EF7F47F31A68A: J900305.3
X5AC892F0D8CDA44E7E18: J900321.3
X5BC1C28EAF5D67603036: J900339.3
X7CA4825DF75BA1068B88: J900311.3
X8D47F4038AE6E42915B2: J900299.3
X9C285D3C07BA239ADB72: J900323.3
X9F47443B516E90FF872D: J900301.3
X37C0D40E8793B92EA1B7: J900329.1
X41B88AA72B8A732B279A: J900315.3
X44CC9CDFCD3CBADF5D00: J900297.1
X53E6848A29A94622ABBC: J900331.3
X65AE667238FA95A8F74F: J900337.3
X92F7EC5BF13E7E12AB51: J900319.1
X110EF417EBA43801D3CA: J900297.3
X494A69F57398E0094B88: J900317.3
X741DF1C2056440887FCB: J900311.1
X763E77DF6D4025E687FA: J900299.1
X1080B5575AB1BB1A0248: J900313.3
X2842A95258EB703DE67C: J900301.1
X03899EF77CFB15DF4250: J900305.1
X6641CDA99062907B3A69: J900321.1
X15938C42644C2F3EFBEE: J900309.1
X17743E5166C7DE548F70: J900323.1
X275914F8D0058F71EFF0: J900303.1
X461891EDAD0B2EB306D7: J900341.3
X7232057F47316092B5DF: J900339.1
X52268074E547F37C1BDF: J900319.3
XA019E807E2A752FFC687: J900327.1
XB528E61191525CCF0307: J900333.3
XBB7C344851AF8D0601AC: J900315.1
XCC1350026597CEE286BE: J900307.1
XCEE2A45C975E1AFE65D9: J900335.3
XD305DDFAE7E0616793A4: J900325.1
XD51322DA5CCAF0966272: J900333.1
XD4682362CD25092A347B: J900307.3
XEC29CCFBAB51F823DB99: J900335.1
XF1EBD465D8DD5809EB46: J900317.1
XF5B9E6F0AF41CB8B8516: J900337.1
XF2827D8A0A013B839CAA: J900343.3
XFEC100AF3DB43E9BF8BD: J900341.1
