Takazudo/zudo-osc-hole-field/boards/osc-core/sheets/board_interfaces_K-p8.kicad_sch

## KiCad design boards/osc-core/sheets/board_interfaces_K-p8.kicad_sch (2026-10-02)

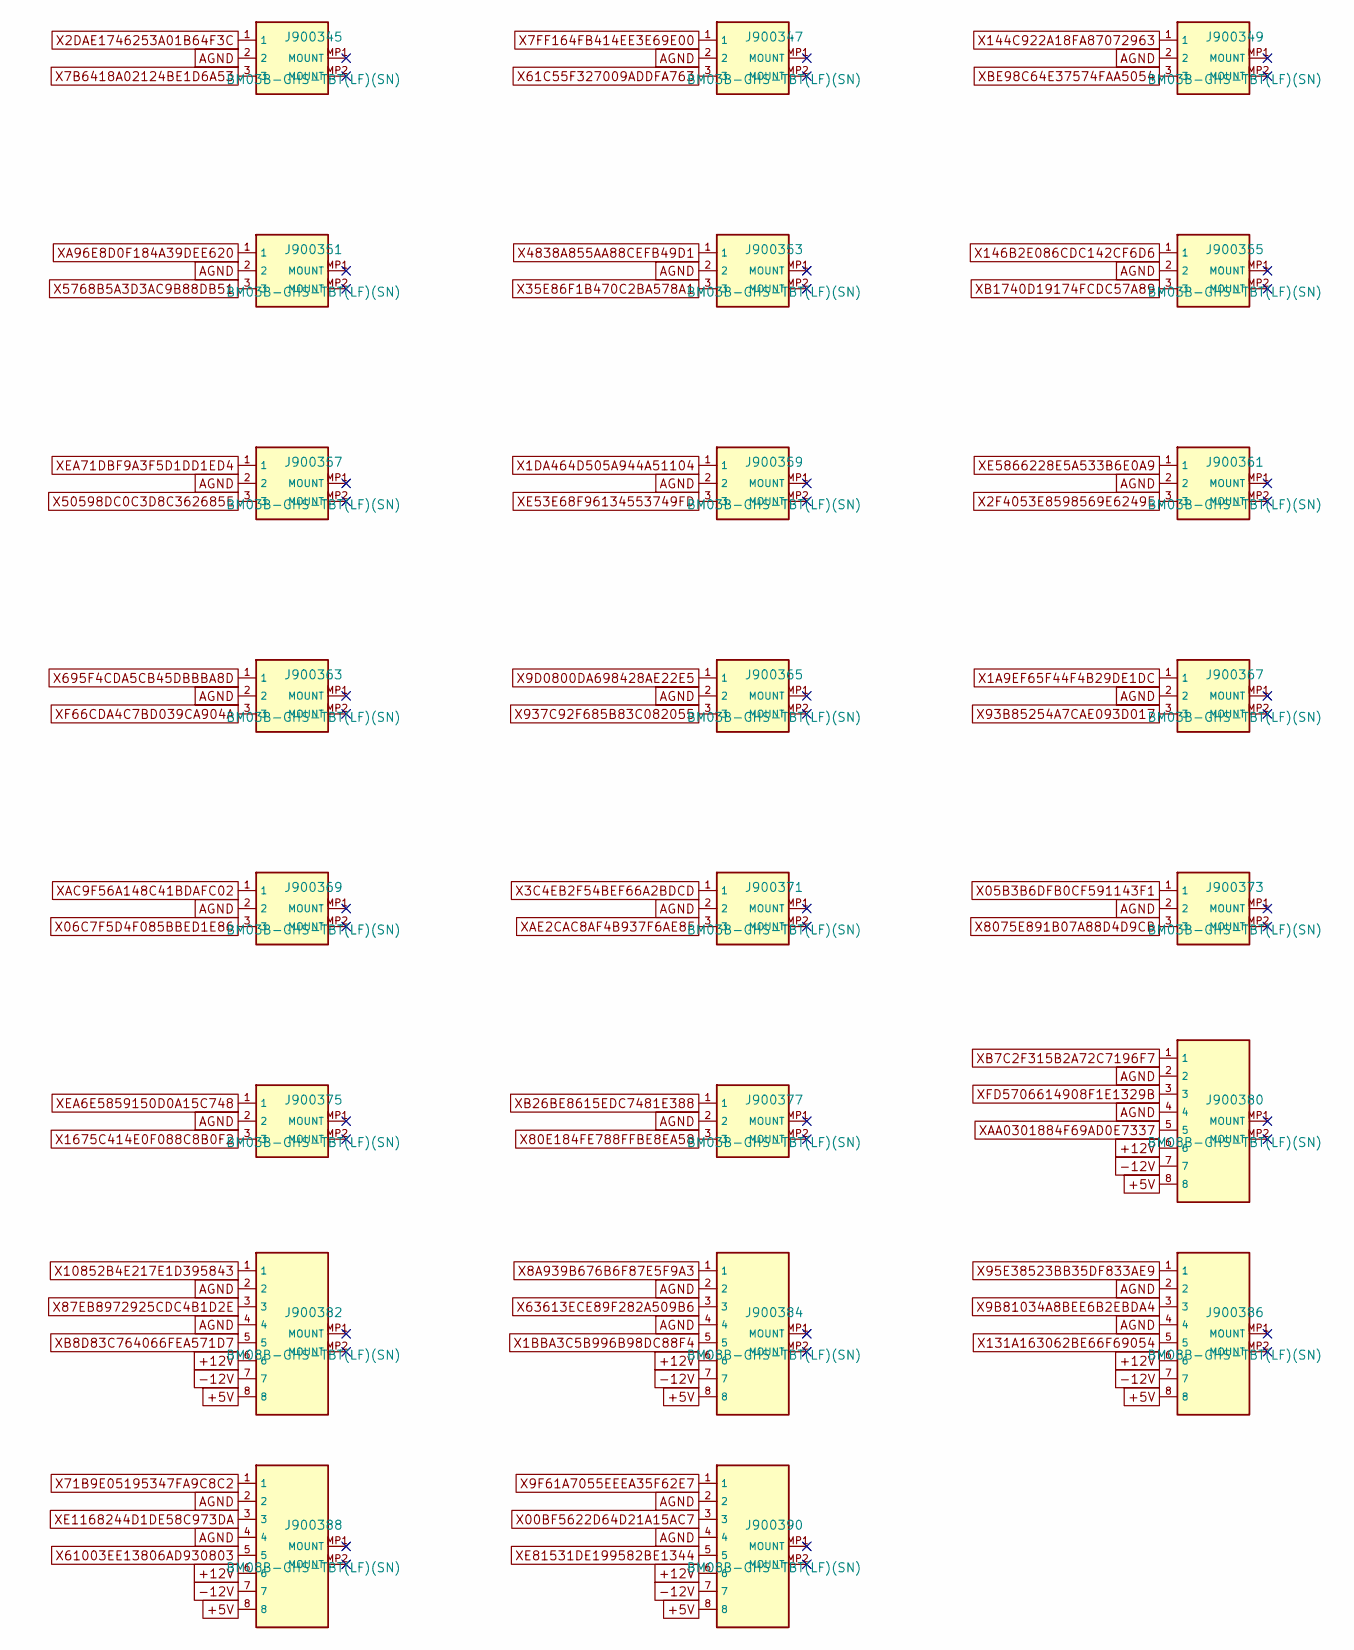
[picture p155: schematic board_interfaces_K-p8.kicad_sch]

Parts:
J900345, J900347, J900349, J900351, J900353, J900355, J900357, J900359, J900361, J900363, J900365, J900367, J900369, J900371, J900373, J900375, J900377: BM03B-GHS-TBT(LF)(SN); JST_GH3_BM_TopEntry; MPN BM03B-GHS-TBT(LF)(SN)
J900380, J900382, J900384, J900386, J900388, J900390: BM08B-GHS-TBT(LF)(SN); JST_GH8_BM_TopEntry; MPN BM08B-GHS-TBT(LF)(SN)

Connections:
+5V: J900380.8, J900382.8, J900384.8, J900386.8, J900388.8, J900390.8
+12V: J900380.6, J900382.6, J900384.6, J900386.6, J900388.6, J900390.6
-12V: J900380.7, J900382.7, J900384.7, J900386.7, J900388.7, J900390.7
AGND: J900345.2, J900347.2, J900349.2, J900351.2, J900353.2, J900355.2, J900357.2, J900359.2, J900361.2, J900363.2, J900365.2, J900367.2, J900369.2, J900371.2, J900373.2, J900375.2, J900377.2, J900380.2, J900380.4, J900382.2, J900382.4, J900384.2, J900384.4, J900386.2, J900386.4, J900388.2, J900388.4, J900390.2, J900390.4
X00BF5622D64D21A15AC7: J900390.3
X1A9EF65F44F4B29DE1DC: J900367.1
X1BBA3C5B996B98DC88F4: J900384.5
X1DA464D505A944A51104: J900359.1
X2DAE1746253A01B64F3C: J900345.1
X2F4053E8598569E6249E: J900361.3
X3C4EB2F54BEF66A2BDCD: J900371.1
X05B3B6DFB0CF591143F1: J900373.1
X06C7F5D4F085BBED1E86: J900369.3
X7B6418A02124BE1D6A53: J900345.3
X7FF164FB414EE3E69E00: J900347.1
X8A939B676B6F87E5F9A3: J900384.1
X9B81034A8BEE6B2EBDA4: J900386.3
X9D0800DA698428AE22E5: J900365.1
X9F61A7055EEEA35F62E7: J900390.1
X35E86F1B470C2BA578A1: J900353.3
X61C55F327009ADDFA763: J900347.3
X71B9E05195347FA9C8C2: J900388.1
X80E184FE788FFBE8EA58: J900377.3
X87EB8972925CDC4B1D2E: J900382.3
X93B85254A7CAE093D017: J900367.3
X95E38523BB35DF833AE9: J900386.1
X131A163062BE66F69054: J900386.5
X144C922A18FA87072963: J900349.1
X146B2E086CDC142CF6D6: J900355.1
X695F4CDA5CB45DBBBA8D: J900363.1
X937C92F685B83C082055: J900365.3
X1675C414E0F088C8B0F2: J900375.3
X4838A855AA88CEFB49D1: J900353.1
X5768B5A3D3AC9B88DB51: J900351.3
X8075E891B07A88D4D9CB: J900373.3
X10852B4E217E1D395843: J900382.1
X50598DC0C3D8C362685E: J900357.3
X61003EE13806AD930803: J900388.5
X63613ECE89F282A509B6: J900384.3
XA96E8D0F184A39DEE620: J900351.1
XAA0301884F69AD0E7337: J900380.5
XAC9F56A148C41BDAFC02: J900369.1
XAE2CAC8AF4B937F6AE8F: J900371.3
XB7C2F315B2A72C7196F7: J900380.1
XB8D83C764066FEA571D7: J900382.5
XB26BE8615EDC7481E388: J900377.1
XB1740D19174FCDC57A89: J900355.3
XBE98C64E37574FAA5054: J900349.3
XE53E68F96134553749FD: J900359.3
XE81531DE199582BE1344: J900390.5
XE1168244D1DE58C973DA: J900388.3
XE5866228E5A533B6E0A9: J900361.1
XEA6E5859150D0A15C748: J900375.1
XEA71DBF9A3F5D1DD1ED4: J900357.1
XF66CDA4C7BD039CA904A: J900363.3
XFD5706614908F1E1329B: J900380.3
