Takazudo/zudo-osc-hole-field/boards/osc-core/sheets/board_interfaces_K-p9.kicad_sch

## KiCad design boards/osc-core/sheets/board_interfaces_K-p9.kicad_sch (2026-09-30)

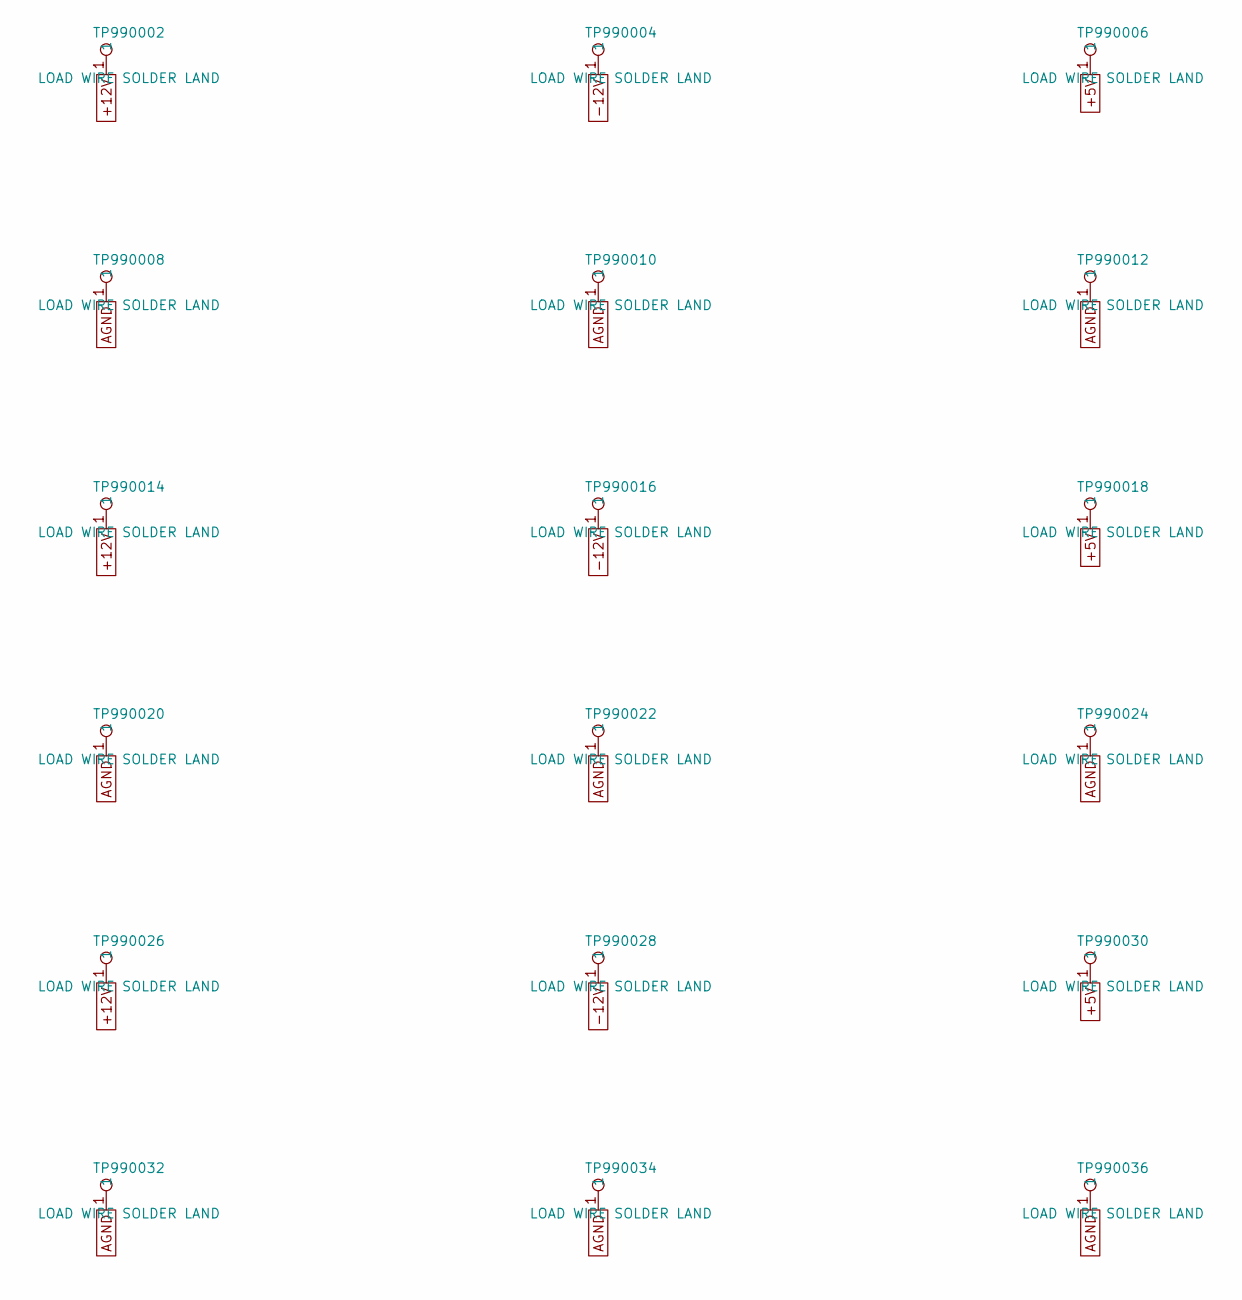
[picture p156: schematic board_interfaces_K-p9.kicad_sch]

Parts:
TP990002, TP990004, TP990006, TP990008, TP990010, TP990012, TP990014, TP990016, TP990018, TP990020, TP990022, TP990024, TP990026, TP990028, TP990030, TP990032, TP990034, TP990036: LOAD WIRE SOLDER LAND; LoadWireTerminal_4x4mm

Connections:
+5V: TP990006.1, TP990018.1, TP990030.1
+12V: TP990002.1, TP990014.1, TP990026.1
-12V: TP990004.1, TP990016.1, TP990028.1
AGND: TP990008.1, TP990010.1, TP990012.1, TP990020.1, TP990022.1, TP990024.1, TP990032.1, TP990034.1, TP990036.1
