Takazudo/zudo-osc-hole-field/boards/osc-core/sheets/board_interfaces_K.kicad_sch

## KiCad design boards/osc-core/sheets/board_interfaces_K.kicad_sch (2026-09-30)

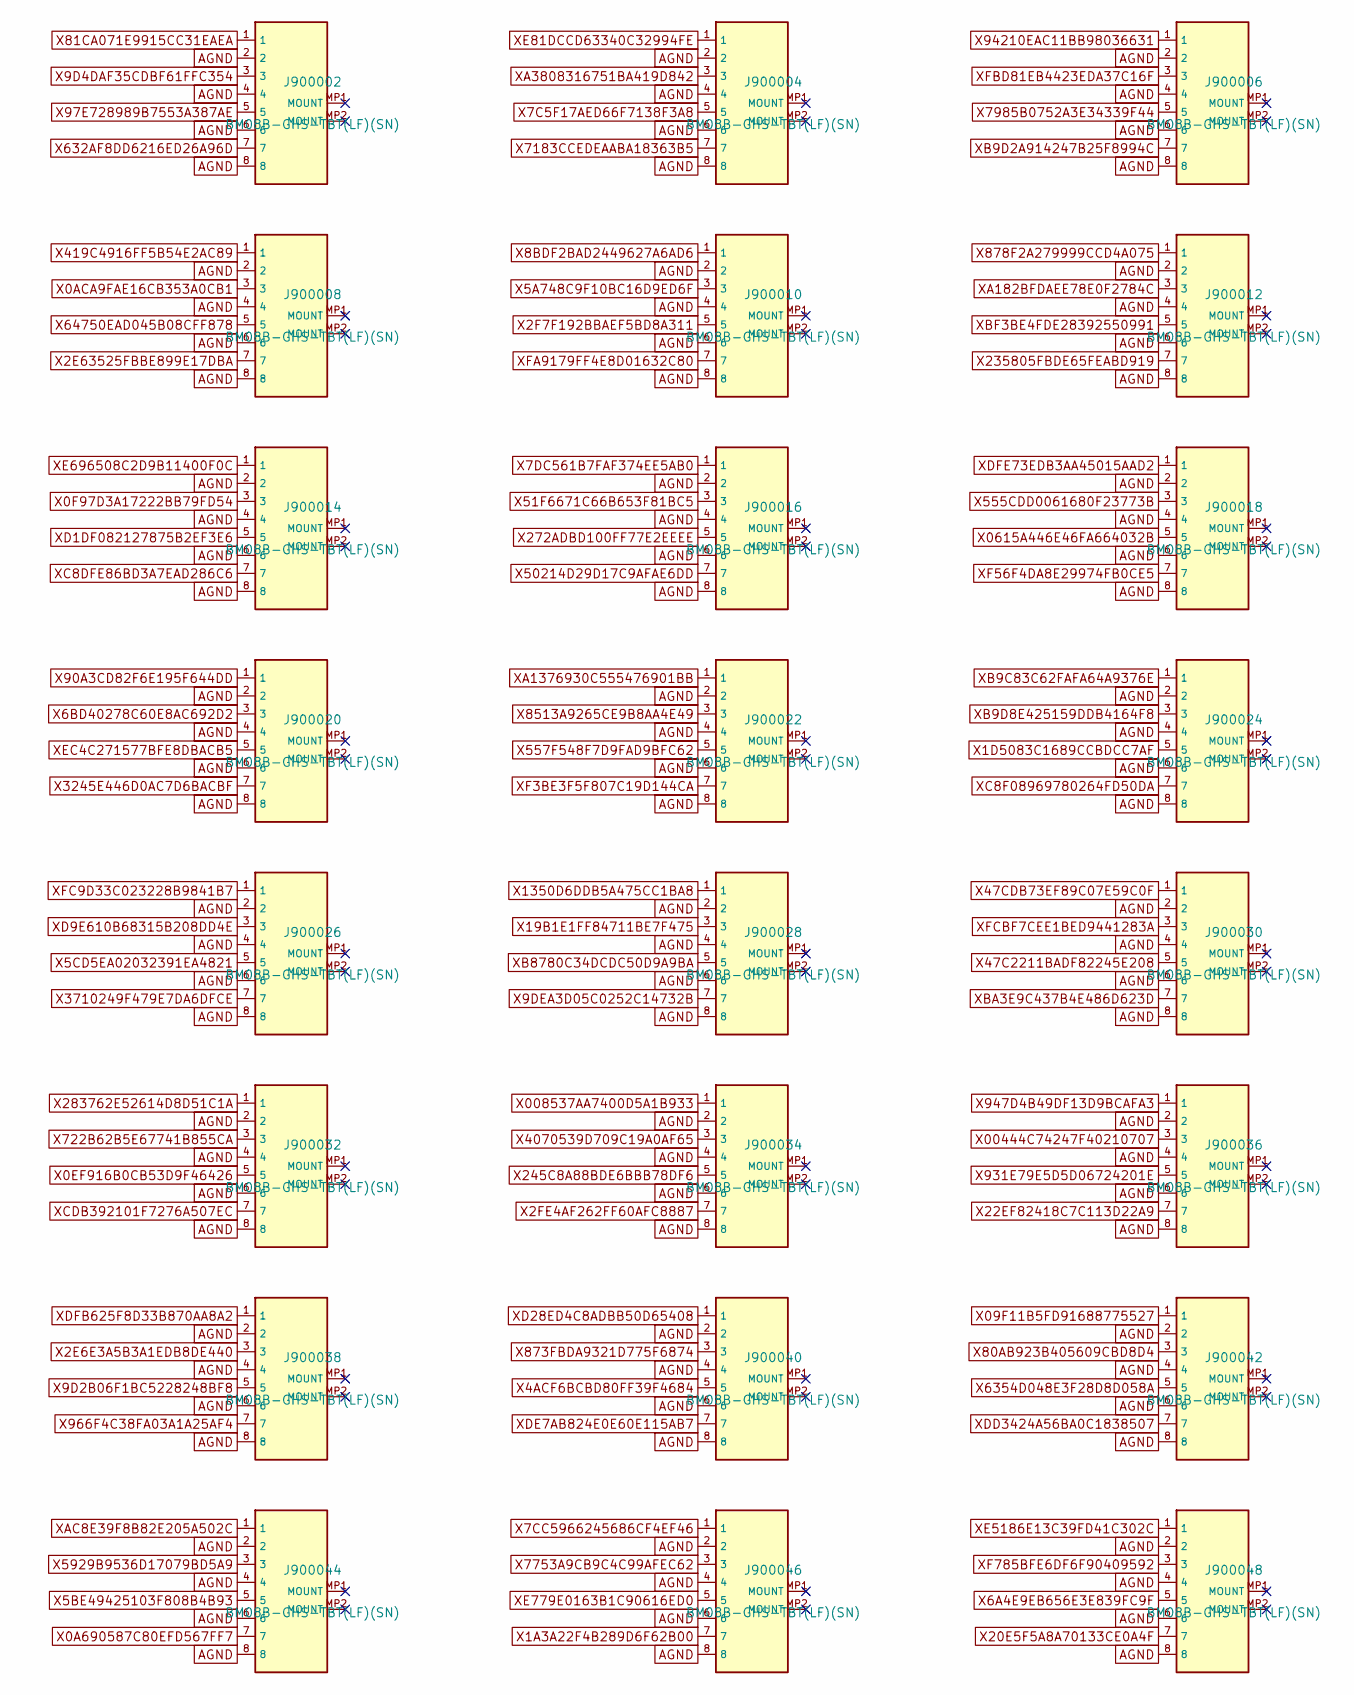
[picture p157: schematic board_interfaces_K.kicad_sch]

Parts:
J900002, J900004, J900006, J900008, J900010, J900012, J900014, J900016, J900018, J900020, J900022, J900024, J900026, J900028, J900030, J900032, J900034, J900036, J900038, J900040, J900042, J900044, J900046, J900048: BM08B-GHS-TBT(LF)(SN); JST_GH8_BM_TopEntry; MPN BM08B-GHS-TBT(LF)(SN)

Connections:
AGND: J900002.2, J900002.4, J900002.6, J900002.8, J900004.2, J900004.4, J900004.6, J900004.8, J900006.2, J900006.4, J900006.6, J900006.8, J900008.2, J900008.4, J900008.6, J900008.8, J900010.2, J900010.4, J900010.6, J900010.8, J900012.2, J900012.4, J900012.6, J900012.8, J900014.2, J900014.4, J900014.6, J900014.8, J900016.2, J900016.4, J900016.6, J900016.8, J900018.2, J900018.4, J900018.6, J900018.8, J900020.2, J900020.4, J900020.6, J900020.8, J900022.2, J900022.4, J900022.6, J900022.8, J900024.2, J900024.4, J900024.6, J900024.8, J900026.2, J900026.4, J900026.6, J900026.8, J900028.2, J900028.4, J900028.6, J900028.8, J900030.2, J900030.4, J900030.6, J900030.8, J900032.2, J900032.4, J900032.6, J900032.8, J900034.2, J900034.4, J900034.6, J900034.8, J900036.2, J900036.4, J900036.6, J900036.8, J900038.2, J900038.4, J900038.6, J900038.8, J900040.2, J900040.4, J900040.6, J900040.8, J900042.2, J900042.4, J900042.6, J900042.8, J900044.2, J900044.4, J900044.6, J900044.8, J900046.2, J900046.4, J900046.6, J900046.8, J900048.2, J900048.4, J900048.6, J900048.8
X0A690587C80EFD567FF7: J900044.7
X0ACA9FAE16CB353A0CB1: J900008.3
X0EF916B0CB53D9F46426: J900032.5
X0F97D3A17222BB79FD54: J900014.3
X1A3A22F4B289D6F62B00: J900046.7
X1D5083C1689CCBDCC7AF: J900024.5
X2E6E3A5B3A1EDB8DE440: J900038.3
X2E63525FBBE899E17DBA: J900008.7
X2F7F192BBAEF5BD8A311: J900010.5
X2FE4AF262FF60AFC8887: J900034.7
X4ACF6BCBD80FF39F4684: J900040.5
X5A748C9F10BC16D9ED6F: J900010.3
X5BE49425103F808B4B93: J900044.5
X5CD5EA02032391EA4821: J900026.5
X6A4E9EB656E3E839FC9F: J900048.5
X6BD40278C60E8AC692D2: J900020.3
X7C5F17AED66F7138F3A8: J900004.5
X7CC5966245686CF4EF46: J900046.1
X7DC561B7FAF374EE5AB0: J900016.1
X8BDF2BAD2449627A6AD6: J900010.1
X9D2B06F1BC5228248BF8: J900038.5
X9D4DAF35CDBF61FFC354: J900002.3
X9DEA3D05C0252C14732B: J900028.7
X09F11B5FD91688775527: J900042.1
X19B1E1FF84711BE7F475: J900028.3
X20E5F5A8A70133CE0A4F: J900048.7
X22EF82418C7C113D22A9: J900036.7
X47C2211BADF82245E208: J900030.5
X47CDB73EF89C07E59C0F: J900030.1
X51F6671C66B653F81BC5: J900016.3
X80AB923B405609CBD8D4: J900042.3
X81CA071E9915CC31EAEA: J900002.1
X90A3CD82F6E195F644DD: J900020.1
X97E728989B7553A387AE: J900002.5
X245C8A88BDE6BBB78DF6: J900034.5
X272ADBD100FF77E2EEEE: J900016.5
X419C4916FF5B54E2AC89: J900008.1
X00444C74247F40210707: J900036.3
X555CDD0061680F23773B: J900018.3
X557F548F7D9FAD9BFC62: J900022.5
X0615A446E46FA664032B: J900018.5
X632AF8DD6216ED26A96D: J900002.7
X722B62B5E67741B855CA: J900032.3
X873FBDA9321D775F6874: J900040.3
X878F2A279999CCD4A075: J900012.1
X931E79E5D5D06724201E: J900036.5
X947D4B49DF13D9BCAFA3: J900036.1
X966F4C38FA03A1A25AF4: J900038.7
X1350D6DDB5A475CC1BA8: J900028.1
X3245E446D0AC7D6BACBF: J900020.7
X5929B9536D17079BD5A9: J900044.3
X6354D048E3F28D8D058A: J900042.5
X7183CCEDEAABA18363B5: J900004.7
X7753A9CB9C4C99AFEC62: J900046.3
X7985B0752A3E34339F44: J900006.5
X8513A9265CE9B8AA4E49: J900022.3
X008537AA7400D5A1B933: J900034.1
X50214D29D17C9AFAE6DD: J900016.7
X64750EAD045B08CFF878: J900008.5
X94210EAC11BB98036631: J900006.1
X235805FBDE65FEABD919: J900012.7
X283762E52614D8D51C1A: J900032.1
X3710249F479E7DA6DFCE: J900026.7
X4070539D709C19A0AF65: J900034.3
XA182BFDAEE78E0F2784C: J900012.3
XA1376930C555476901BB: J900022.1
XA3808316751BA419D842: J900004.3
XAC8E39F8B82E205A502C: J900044.1
XB9C83C62FAFA64A9376E: J900024.1
XB9D2A914247B25F8994C: J900006.7
XB9D8E425159DDB4164F8: J900024.3
XB8780C34DCDC50D9A9BA: J900028.5
XBA3E9C437B4E486D623D: J900030.7
XBF3BE4FDE28392550991: J900012.5
XC8DFE86BD3A7EAD286C6: J900014.7
XC8F08969780264FD50DA: J900024.7
XCDB392101F7276A507EC: J900032.7
XD1DF082127875B2EF3E6: J900014.5
XD9E610B68315B208DD4E: J900026.3
XD28ED4C8ADBB50D65408: J900040.1
XDD3424A56BA0C1838507: J900042.7
XDE7AB824E0E60E115AB7: J900040.7
XDFB625F8D33B870AA8A2: J900038.1
XDFE73EDB3AA45015AAD2: J900018.1
XE81DCCD63340C32994FE: J900004.1
XE779E0163B1C90616ED0: J900046.5
XE5186E13C39FD41C302C: J900048.1
XE696508C2D9B11400F0C: J900014.1
XEC4C271577BFE8DBACB5: J900020.5
XF3BE3F5F807C19D144CA: J900022.7
XF56F4DA8E29974FB0CE5: J900018.7
XF785BFE6DF6F90409592: J900048.3
XFA9179FF4E8D01632C80: J900010.7
XFBD81EB4423EDA37C16F: J900006.3
XFC9D33C023228B9841B7: J900026.1
XFCBF7CEE1BED9441283A: J900030.3
