Takazudo/zudo-osc-hole-field/boards/osc-core/sheets/envelope_E1_K.kicad_sch

## KiCad design boards/osc-core/sheets/envelope_E1_K.kicad_sch (2026-10-05)

Schematic: envelope_E1_K.kicad_sch

Parts:
C4101: 1e-07 F; C0603; MPN GRM188R71H104KA93D
C4102: 1e-06 F; C0603
C4108: 1 µF; C0603
C4109: 1 nF C0G; C0603
C4110, C4113: 100 nF C0G; C1206; MPN 1206CG104J500NT; LCSC C46348
C4111, C4112: 1e-08 F; C0603
C4114, C4121, C4122, C4123, C4124, C4125, C4126, C4127, C4128, C4129, C4130, C4131, C4132, C4133, C4134, C4135, C4136, C4137, C4138, C4139, C4140, C4141, C4142, C4143, C4144, C4145, C4146, C4147, C4148, C4149, C4150, C4151, C4152, C4153, C4154, C4155, C4157, C4158, C4159, C4160, C4161, C4162, C4163, C4166, C4167, C4168, C4169, C4170, C4171: 100 nF; C0603; MPN GRM188R71H104KA93D
D4104: BAS16GW-QX; SOD-123; MPN BAS16GW-QX
D4105, D4106: BAT54S,215; SOT-23; MPN BAT54S,215
Q4101, Q4104: BCM847BS,115; SOT-363_SC-70-6; MPN BCM847BS,115
Q4102, Q4103, Q4105, Q4106: MMBT3906,215; SOT-23; MPN MMBT3906,215
R4101, R4102, R4119: 10000 Ω; R0603
R4103: 22000 Ω; R0603
R4104, R4117: 100000 Ω; R0603; MPN RT0603BRD07100KL
R4118: 33200 Ω; R0603
R4120: 390000 Ω; R0603
R4121: 4700 Ω; R0603
R4132, R4136, R4138, R4143, R4145, R4151, R4153, R4154, R4155, R4157, R4168, R4170, R4171, R4172, R4174, R4183, R4184, R4185, R4186, R4187, R4188, R4189, R4190: 100 kΩ; R0603; MPN RT0603BRD07100KL
R4133, R4134: 47 kΩ; R0603
R4135: 60 kΩ; R0603
R4137: 80 kΩ; R0603
R4139: 40 kΩ; R0603
R4140, R4156, R4173: 10 kΩ; R0603
R4141: 79 kΩ; R0603
R4142, R4162, R4163, R4179, R4180: 22 kΩ; R0603
R4144, R4146: 10 MΩ; R0603
R4147, R4148: 4.7 kΩ; R0603
R4149, R4166: 1000 Ω; R0603
R4150, R4167: 1e+07 Ω; R0603
R4152, R4158, R4169, R4175: 200 kΩ; R0603
R4159, R4176: 3.3 kΩ; R0603
R4160, R4165, R4177, R4182, R4192, R4194: 1 kΩ; R0603
R4161, R4178: 300 kΩ; R0603
R4164, R4181: 470 kΩ; R0603
R4191, R4193: 899 kΩ; R0603
R4195, R4196, R4197, R4198: 100 Ω; R0603
R4199: 64 kΩ; R0603
RB4101: 80 kΩ; R0603
RB4102, RB4103: 100 kΩ; R0603; MPN RT0603BRD07100KL
RB4104: 400 kΩ; R0603
RV4102, RV4106: 1 kΩ; Potentiometer_Bourns_TC33X_Vertical; MPN TC33X-2-102E
RV4103, RV4107: 50 kΩ; Potentiometer_Bourns_TC33X_Vertical
RV4104, RV4108: 10 kΩ; Potentiometer_Bourns_TC33X_Vertical; MPN TC33X-2-103E
U4101: REF5050AIDR; SOIC-8_3.9x4.9mm_P1.27mm; MPN REF5050AIDR; LCSC C27804
U4105: CD74HC221M96; SOIC-16_3.9x9.9mm_P1.27mm; MPN CD74HC221M96; LCSC C133954
U4106, U4108: ADG5412FBRUZ; TSSOP-16_4.4x5mm_P0.65mm; MPN ADG5412FBRUZ; LCSC C579073
U4107: LM13700M/NOPB; SOIC-16_3.9x9.9mm_P1.27mm; MPN LM13700M/NOPB; LCSC C1346265
U4109, U4110: LM393BIDR; SOIC-8_3.9x4.9mm_P1.27mm; MPN LM393BIDR
U4112: SN74HC14DR; SOIC-14_3.9x8.7mm_P1.27mm; MPN SN74HC14DR
U4113, U4114, U4115, U4116, U4117, U4118, U4119, U4120, U4121, U4122, U4123, U4124, U4125, U4126, U4127, U4128, U4129: SN74HC00DR; SOIC-14_3.9x8.7mm_P1.27mm; MPN SN74HC00DR
U4130, U4131, U4132, U4133, U4134, U4135, U4136, U4137, U4138: SN74HC74DR; SOIC-14_3.9x8.7mm_P1.27mm; MPN SN74HC74DR
U4139, U4140, U4141: OPA4197IPWR; TSSOP-14_4.4x5mm_P0.65mm; MPN OPA4197IPWR; LCSC C2057327
U4143, U4144, U4145: OPA4196IDR; SOIC-14_3.9x8.7mm_P1.27mm; MPN OPA4196IDR; LCSC C2057385

Connections:
+5V: C4121.1, C4130.1, C4131.1, C4132.1, C4133.1, C4134.1, C4135.1, C4136.1, C4137.1, C4138.1, C4139.1, C4140.1, C4141.1, C4142.1, C4143.1, C4144.1, C4145.1, C4146.1, C4147.1, C4148.1, C4149.1, C4150.1, C4151.1, C4152.1, C4153.1, C4154.1, C4155.1, C4157.1, D4104.1 (K), R4121.1, R4132.1, R4134.1, R4147.1, R4148.1, U4105.16 (VCC), U4112.14 (VCC), U4113.14 (VCC), U4114.14 (VCC), U4115.14 (VCC), U4116.14 (VCC), U4117.14 (VCC), U4118.14 (VCC), U4119.14 (VCC), U4120.14 (VCC), U4121.14 (VCC), U4122.14 (VCC), U4123.14 (VCC), U4124.14 (VCC), U4125.14 (VCC), U4126.14 (VCC), U4127.14 (VCC), U4128.14 (VCC), U4129.14 (VCC), U4130.2 (D), U4130.4 (~S), U4130.10 (~S), U4130.14 (VCC), U4131.4 (~S), U4131.10 (~S), U4131.14 (VCC), U4132.4 (~S), U4132.10 (~S), U4132.14 (VCC), U4133.4 (~S), U4133.10 (~S), U4133.14 (VCC), U4134.4 (~S), U4134.10 (~S), U4134.14 (VCC), U4135.4 (~S), U4135.10 (~S), U4135.14 (VCC), U4136.4 (~S), U4136.10 (~S), U4136.14 (VCC), U4137.4 (~S), U4137.10 (~S), U4137.14 (VCC), U4138.4 (~S), U4138.10 (~S), U4138.14 (VCC)
+12V: C4101.1, C4114.1, C4122.1, C4124.1, C4126.1, C4128.1, C4129.1, C4158.1, C4160.1, C4162.1, C4166.1, C4168.1, C4170.1, Q4102.2 (E), Q4103.2 (E), Q4105.2 (E), Q4106.2 (E), U4101.2 (Vin), U4106.13 (VDD), U4107.11 (V+), U4108.13 (VDD), U4109.8 (V+), U4110.8 (V+), U4139.4 (V+), U4140.4 (V+), U4141.4 (V+), U4143.4 (V+), U4144.4 (V+), U4145.4 (V+)
-12V: C4123.1, C4125.1, C4127.1, C4159.1, C4161.1, C4163.1, C4167.1, C4169.1, C4171.1, U4106.4 (VSS), U4107.6 (V-), U4108.4 (VSS), U4139.11 (V-), U4140.11 (V-), U4141.11 (V-), U4143.11 (V-), U4144.11 (V-), U4145.11 (V-)
AGND: C4101.2, C4102.2, C4108.2, C4109.2, C4111.2, C4112.2, C4113.2, C4114.2, C4121.2, C4122.2, C4123.2, C4124.2, C4125.2, C4126.2, C4127.2, C4128.2, C4129.2, C4130.2, C4131.2, C4132.2, C4133.2, C4134.2, C4135.2, C4136.2, C4137.2, C4138.2, C4139.2, C4140.2, C4141.2, C4142.2, C4143.2, C4144.2, C4145.2, C4146.2, C4147.2, C4148.2, C4149.2, C4150.2, C4151.2, C4152.2, C4153.2, C4154.2, C4155.2, C4157.2, C4158.2, C4159.2, C4160.2, C4161.2, C4162.2, C4163.2, C4166.2, C4167.2, C4168.2, C4169.2, C4170.2, C4171.2, D4105.1 (A), D4106.1 (A), Q4101.2 (B1), Q4104.2 (B1), R4104.2, R4136.2, R4138.2, R4140.2, R4142.2, R4150.2, R4165.2, R4167.2, R4182.2, R4184.2, R4190.2, R4192.2, R4194.2, RB4101.2, RB4104.2, U4101.4 (GND), U4105.1 (1A), U4105.8 (GND), U4105.9 (2A), U4105.10 (2B), U4105.11 (2R), U4106.5 (GND), U4107.7, U4107.10, U4108.5 (GND), U4108.6 (S4), U4108.7 (D4), U4108.8 (IN4), U4108.9 (IN3), U4108.10 (D3), U4108.11 (S3), U4108.15 (D2), U4109.4 (GND), U4110.4 (GND), U4110.5 (+), U4112.7 (GND), U4113.7 (GND), U4114.7 (GND), U4115.7 (GND), U4116.7 (GND), U4117.7 (GND), U4118.7 (GND), U4119.7 (GND), U4120.7 (GND), U4121.7 (GND), U4122.7 (GND), U4123.7 (GND), U4124.7 (GND), U4125.7 (GND), U4126.7 (GND), U4127.7 (GND), U4128.7 (GND), U4129.7 (GND), U4129.12, U4129.13, U4130.7 (GND), U4131.7 (GND), U4132.7 (GND), U4133.7 (GND), U4134.7 (GND), U4135.7 (GND), U4136.7 (GND), U4137.7 (GND), U4138.7 (GND), U4138.11 (C), U4138.12 (D), U4138.13 (~R), U4139.5 (+), U4140.10 (+), U4140.12 (+), U4141.3 (+), U4141.5 (+), U4141.12 (+), U4143.5 (+), U4143.10 (+), U4144.5 (+), U4144.10 (+), U4145.12 (+)
X0A50AE22ADC0575BFB6C: U4124.3, U4124.12
X0AC854C35960FD8C89FF: R4183.2, R4184.1, U4145.3 (+)
X0B9BAABE71147600F45A: U4114.3, U4114.4
X0B475DAB16A59C025E35: U4124.1, U4124.4, U4124.5
X0B0796C6CAB8D003C2DB: Q4102.1 (B), Q4102.3 (C), Q4103.1 (B), R4162.1
X0B6656D920B04D442315: R4155.1, R4156.1, U4143.8
X0CDB5BC41E59173EAB13: R4157.1, U4143.13 (-), U4143.14
X0D0960DD460C3186BB10: C4110.2, U4105.14 (1CX)
X0D938485C23072FBF110: U4127.11, U4128.1, U4128.2
X0E4A19C71F03DA55B745: Q4104.6 (C1), RV4107.2 (Wiper), RV4107.3 (CW), U4141.6 (-)
X1BC15E8A792F37E41412: U4108.16 (IN2), U4125.11
X1D9B50C9004A7E7EB8F5: R4151.1, U4143.1, U4143.2 (-)
X1D10D3B0EA8A6674EFB5: Q4101.1 (E1), Q4101.4 (E2), U4140.14
X2A257C4D7F67AB25A2D7: U4118.11, U4119.1, U4119.2
X2A5779A8F7538EB8DA7D: D4105.3 (COM), R4156.2, U4143.12 (+)
X2B2FD6CD1D1554A8B31B: U4132.2 (D)
X2BABCD1F4A2DFB270E50: Q4101.6 (C1), RV4103.2 (Wiper), RV4103.3 (CW), U4140.13 (-)
X2BB905E42AB98D1B458E: R4198.1, U4108.14 (S2)
X2BFCCE38A588804F6F06: U4123.11, U4138.2 (D)
X2C0D9AEDC7035F705868: U4106.9 (IN3), U4128.8
X2E3730128E1692239755: C4109.1, R4133.2, U4112.9
X2F9FAE0DB22A57E8D84D: U4125.8, U4125.12
X2F18EDA340050412B909: U4122.6, U4137.12 (D)
X3AB46E186A030DFD9757: U4114.5, U4137.8 (~Q)
X3B1D630FD6EB6F31F170: R4103.2, R4104.1, U4139.10 (+)
X3B8A935F71B2C6D50683: R4181.2, R4182.1, U4107.14 (+)
X03CDF7016288E3B6DFC2: U4106.16 (IN2), U4128.3
X3D982D7E890C2A2B54F4: R4117.2, R4118.2, U4109.2 (-)
X4A20606D76EEAB0ACAE0: U4116.4, U4118.5, U4120.1, U4132.9 (Q)
X4D02A46262F8578D6551: U4130.5 (Q), U4130.12 (D)
X4E3C454F2F7CC73EED87: U4117.3, U4117.10
X4E4F9E3B233E3D30E9A1: R4141.2, R4142.1, U4110.2 (-)
X4E931D7C0708176F3861: R4137.2, R4138.1, U4140.2 (-)
X4F60704F7F7DDCC4563F: U4126.8, U4127.5, U4128.5
X05C26B46F3BBE46CF3D9: U4106.8 (IN4), U4129.3
X5C4362A8D9C94634FC50: U4114.6, U4114.9, U4114.10, U4125.5
X5D458FCCA0E0C13A9D54: U4120.8, U4120.13
X5EE48DDEF74404E5CB99: U4120.6, U4120.9
X5EF79DE751E11CF42B43: U4116.8, U4116.12, U4116.13
X5F945444046B5DCD2CD1: R4159.1, R4160.1, U4140.8
X6E47CCE2A7EEDA0071C7: R4195.1, U4107.5
X7A0B5258E48FBD5EB856: C4108.1, D4104.2 (A), R4132.2, U4112.3
X7A4C27BCA887554B7928: U4128.6, U4128.9, U4128.10
X7BAB4C48FE0B63EBB671: U4112.12, U4125.2, U4135.12 (D)
X7CEB538A6D7787C710EB: U4119.11, U4121.4
X7DACC0A0EB67BAAD39AE: U4135.9 (Q), U4136.2 (D)
X7F23D62861971D624E7E: R4154.2, R4155.2, U4143.9 (-)
X7FF9C8B455C21DD1985F: U4112.4, U4112.5
X8A880EACFE751F68BB4D: R4157.2, R4158.2, RV4102.2 (Wiper), RV4102.3 (CW), U4140.9 (-)
X8BB363BE87DD196DF027: U4116.3, U4117.4, U4117.5
X8BE85DDEF9785B99ED40: U4128.11, U4129.1, U4129.2
X8CCA5ABD62E47B5D9EE7: C4102.1, U4101.6 (Vout), U4139.3 (+)
X8D3C9A56AF6E2F1539A5: U4116.11, U4117.1
X8D7FC417EC2FC63F0470: R4186.1, U4106.15 (D2), U4145.1
X8D31D41294342B12A350: U4117.13, U4120.4, U4135.5 (Q)
X8E0D27D84F40BBB117C9: R4137.1, R4143.1, R4183.1, U4106.3 (S1), U4106.10 (D3), U4140.1
X8F2A216449F018AFB746: U4119.6, U4119.9, U4119.10
X8F6C97B2E5A571EE4F9D: U4119.12, U4122.10, U4124.2, U4125.1, U4129.9, U4129.10, U4137.9 (Q)
X9B839E7FF9376870A32D: R4139.2, R4140.1, U4140.5 (+)
X9EA963DD7C5941FC78C2: R4135.2, R4136.1, U4139.13 (-)
X13C1011CBC4FA61920B3: U4121.1, U4137.5 (Q)
X17D4FDC40CFD180B1BD2: U4133.2 (D)
X19C7099F0D460CA2DF89: U4119.3, U4119.4
X28E88883A5968BC969B0: Q4103.3 (C), R4163.1
X34C5B67D5750D8ED7449: R4193.2, R4194.1, U4107.13 (-)
X34FB2F5178AFFF57ADAA: R4143.2, R4144.2, U4109.5 (+)
X43ABCB494D5CB2C10AB9: U4134.9 (Q), U4135.2 (D)
X48A4E0F74F630C42D873: U4116.5, U4131.8 (~Q)
X54B01F8C60F023EF7C78: R4101.2, R4102.2, U4139.6 (-)
X55C8D221BB611B672DCE: R4189.2, R4190.1, U4145.6 (-)
X058BE71DAF00A5A01CA2: R4152.1
X60C95A6ED897403101EE: Q4106.3 (C), R4180.1
X63E7BF75B38A42841C5D: U4126.3, U4126.5
X64A0178AAAF3EF67470E: U4121.3, U4121.13
X66A7935339B0FF687ED4: Q4104.3 (C2), R4179.2
X68BD3C5141C0DDC690E3: U4114.8, U4115.5
X71E2D0CA02FED9642DA1: R4176.2, RV4106.1 (CCW)
X79CD5640C71990AE294D: R4168.2, R4169.2, R4170.2, U4144.6 (-)
X85D909FBF582A5BD0B18: U4113.8, U4131.2 (D)
X85F7DB28A1E084E06E61: R4133.1, U4112.8, U4130.3 (C), U4130.11 (C), U4131.3 (C), U4131.11 (C), U4132.3 (C), U4132.11 (C), U4133.3 (C), U4133.11 (C), U4134.3 (C), U4134.11 (C), U4135.3 (C), U4135.11 (C), U4136.3 (C), U4136.11 (C), U4137.3 (C), U4137.11 (C), U4138.3 (C)
X87BEDB8DF07BE69D267E: U4113.13, U4118.1, U4126.4, U4137.6 (~Q)
X89DF9C27EF65A5940B07: R4135.1, U4108.3 (S1), U4139.14
X93F84BDE503B3DB9566D: R4171.2, R4172.2, U4144.9 (-)
X98D136E285DCC4EE60ED: U4120.3, U4120.5, U4121.2
X151AD6B4E988533D1ECE: U4141.13 (-), U4141.14
X214ED5A8892039CF8AA7: D4105.2 (K), D4106.2 (K), R4101.1, R4103.1, R4118.1, R4139.1, R4141.1, R4161.1, R4178.1, RB4102.1, RV4104.3 (CW), RV4108.3 (CW), U4110.6 (-), U4139.1, U4139.2 (-), U4139.12 (+), U4140.3 (+)
X261CC6AD3B59CA4F4290: U4120.11, U4121.5
X537DBD1AA495A8A0DB95: U4124.6, U4124.9
X716C83E78788AEFFA25E: R4181.1, RV4108.2 (Wiper)
X725AB67BC73000B6171A: U4123.8, U4123.12, U4123.13
X810D55299216F4246B1A: U4108.1 (IN1), U4126.6
X904DAC27D0407C5CAAF0: R4164.1, RV4104.2 (Wiper)
X933A94DFC541891C8EF6: R4161.2, RV4103.1 (CCW)
X3256A7149DC594423760: U4119.8, U4137.2 (D)
X3355FE2989D53281A601: U4115.8, U4115.12
X3667DB1937542EB0C6C5: R4146.1, R4148.2, U4110.1, U4112.13
X3961F0F3739A44559577: U4112.2, U4113.1, U4113.2
X4540EF74C0F6C007902E: U4117.8, U4136.12 (D)
X5350F9B9F5359118DD91: U4124.8, U4124.13
X6756FD19618BEC8EB562: U4122.11, U4123.1, U4128.4, U4128.12
X6989F0D5C243DDFAAD15: RB4103.1, U4145.8
X7105D8F3B5C15DB5A3F7: U4127.6, U4127.9, U4127.10
X7296DBB4AD029BCC2AAB: R4153.1, R4154.1, U4143.7
X7906A2435E0E609C6C03: RB4102.2, RB4103.2, RB4104.1, U4145.9 (-)
X8839D0236D2A670F3DD7: U4118.3, U4119.5
X11270A124B43E79A4266: U4106.1 (IN1), U4127.8
X21865D5691F958DB8F2D: U4124.11
X24874CAFAB1396832011: R4188.1, U4140.6 (-), U4140.7
X25788D7048AF0873547F: R4164.2, R4165.1, U4107.4 (-)
X37083A3A67E9B296FC65: R4180.2, U4107.16
X55001F99BA3864011D76: U4121.8, U4121.12
X56974B36DF2C94412360: U4121.6, U4121.9, U4121.10
X63935D2717667935B98A: R4174.1, U4144.13 (-), U4144.14
X69889FE2A42CA13A1574: R4191.1, U4106.2 (D1), U4106.14 (S2)
X76607FB53D44DC83479A: U4118.8, U4118.12
X83715BFDCBC6D0BF7C49: U4113.12, U4136.8 (~Q)
X89335CB7490BAA13F961: U4114.12, U4118.13, U4120.2, U4131.9 (Q), U4134.2 (D)
X99165EB94B65587AB7D9: U4126.11, U4127.1, U4127.2
X168782A1E879F585872F: U4118.6, U4118.9, U4118.10
X528040CD36A4C0CB9976: U4132.5 (Q), U4132.12 (D)
X667413A9D525833F4F71: U4113.3, U4113.9
X855618E0B72C253EA6F2: R4176.1, R4177.1, U4141.1
X925702C460883245FBEE: R4172.1, R4173.1, U4144.8
X51000375EC45A8995D7B: U4117.11, U4118.2
X906806551BF8D9E5B830: U4123.2, U4136.5 (Q)
X2773841554C8CC811FE1: U4119.13, U4136.6 (~Q)
X7095319889A89ED13B7A: R4197.1, U4108.2 (D1)
XA0AAE7E18201DACFDDC3: R4187.2, R4188.2, U4145.5 (+)
XA1ACAB7997D16E5CE81C: C4112.1, R4166.2, R4167.1, U4144.3 (+)
XA7ED772F5BE24C1115D2: Q4104.1 (E1), Q4104.4 (E2), U4141.7
XA9ACCDE9258DFEDFEA5B: C4111.1, R4149.2, R4150.1, U4143.3 (+)
XA10E87A7282D0598D9FA: U4122.8, U4122.12, U4122.13
XA25FB62B02A79E304449: R4191.2, R4192.1, U4107.3 (+)
XA83E8C2B123ED263B603: C4113.1, R4195.2, R4196.2, R4197.2, R4198.2, U4141.10 (+)
XA95BEC84ECFC0E82D5BB: C4110.1, R4134.2, U4105.15 (1RXCX)
XA971E518BF3F7288E31E: U4122.3, U4122.4, U4122.5
XAA0301884F69AD0E7337: U4129.8
XAC64AF2ED290A76AAD3A: R4170.1, R4171.1, U4144.7
XAC269F123A9270AAFBEA: R4193.1, U4106.6 (S4), U4106.11 (S3)
XAD04E5A487ED3EA97A0C: U4112.10, U4126.2, U4134.12 (D)
XAF094CB16DFFD655185B: U4145.13 (-), U4145.14
XAFE12BEA6818454211EC: U4115.11, U4116.2
XB01DA53372CF61D6B865: U4113.6, U4113.10
XB2C032E73F741CFB35BD: R4168.1, U4144.1, U4144.2 (-)
XB3EDE32A0C577E92F4DD: R4119.1, U4139.8, U4139.9 (-)
XB7C2F315B2A72C7196F7: R4185.1, R4187.1, R4199.1, U4141.8, U4141.9 (-)
XB18F9D7E988932165DD2: R4185.2, R4186.2, U4145.2 (-)
XB66E196D7399A865DFDB: R4169.1
XB160D60D731A8E0D7FF7: Q4104.5 (B2), R4177.2
XB851D4953A787339082E: U4123.3, U4123.4, U4123.5
XB546678299434544507C: U4131.5 (Q), U4131.12 (D)
XBA48267F34D7D0FB64EC: R4178.2, RV4107.1 (CCW)
XBAE2A960EE1882903857: U4117.6, U4117.9, U4118.4, U4122.1, U4123.10
XBCA4688CC73D43650238: U4126.9, U4126.10, U4127.13, U4128.13
XBE6F759D303A189ECA9B: D4106.3 (COM), R4173.2, U4144.12 (+)
XBE3741E164E3D39DDD13: U4116.6, U4117.2, U4120.10
XC0AF46342A3E0236CC81: U4114.13, U4134.6 (~Q)
XC0EF32DD514C3BC69B8B: U4115.3, U4115.13
XC3FD7E3BDC68EB058B83: U4127.3, U4127.4, U4127.12
XC26D45F007A29FB1B40B: R4119.2, R4120.2, U4109.3 (+)
XC482CD93B529547D7BCC: U4125.3, U4125.13
XC960027B02DECF254F85: U4105.4 (1Q), U4115.1, U4115.2
XC29302533823F8B79991: U4121.11, U4122.2
XCA00C997CF1D9DD0B0A0: R4145.2, R4146.2, U4110.3 (+)
XCB920A0E756AB8BBF722: U4105.2 (1B), U4138.5 (Q)
XCCCAB78611B006E208B7: R4149.1
XCD1B35E26F74529DDE12: R4117.1
XD4EA05C2BFB4502FC5B8: R4163.2, U4107.1
XD7DD173C6FE96C42CC27: Q4101.5 (B2), R4160.2
XD08FF0C6245961CE5A9C: U4112.6, U4130.1 (~R), U4130.13 (~R)
XD525C1521D6573A10FC6: R4174.2, R4175.2, RV4106.2 (Wiper), RV4106.3 (CW), U4141.2 (-)
XD5338D5835B5E2BD74C2: Q4101.3 (C2), R4162.2
XD876685D2F28C69B68C5: U4133.5 (Q), U4133.12 (D)
XDB2168B8C8972F325D70: U4116.10, U4135.6 (~Q)
XDC18A298DEFD52CBCC3D: R4196.1, U4107.12
XE3C173C3F298263E5D9E: U4113.11, U4114.1, U4114.2
XE16DF9710AFE695C83CF: R4159.2, RV4102.1 (CCW)
XE59A05D839B7311C312F: R4144.1, R4147.2, U4109.7, U4112.11
XEA57FE515C670A757DC4: R4151.2, R4152.2, R4153.2, U4143.6 (-)
XEF95196AE92551105499: U4105.3 (1R), U4122.9, U4125.4, U4126.12, U4130.9 (Q), U4131.1 (~R), U4131.13 (~R), U4132.1 (~R), U4132.13 (~R), U4133.1 (~R), U4133.13 (~R), U4134.1 (~R), U4134.13 (~R), U4135.1 (~R), U4135.13 (~R), U4136.1 (~R), U4136.13 (~R), U4137.1 (~R), U4137.13 (~R), U4138.1 (~R)
XF8E9F9D3244B518DDA3F: U4116.9, U4117.12, U4120.12, U4124.10, U4126.1, U4126.13, U4129.4, U4129.5, U4136.9 (Q)
XF10BBD3F85F8C2FD18F1: U4114.11, U4116.1
XF14E8FA3C9B302019860: U4125.6, U4125.9, U4125.10
XF48A01C32A245208724B: R4145.1, R4189.1, U4106.7 (D4), U4109.6 (-), U4145.7
XF54E77C0E32924534D70: U4113.4, U4113.5
XF77FD0E2252C62EB0E27: U4123.6, U4123.9
XF818C084D8A97A8D4659: U4115.6, U4115.9, U4115.10
XFB0644432B15DB7BBF4C: R4102.1, R4158.1, R4175.1, RV4104.1 (CCW), RV4108.1 (CCW), U4139.7
XFC009EE21B2220681005: Q4105.1 (B), Q4105.3 (C), Q4106.1 (B), R4179.1
XFCF31C83A99DE3B02021: R4199.2, RB4101.1, U4145.10 (+)
XFCFF584FFE054CAA6DC8: R4120.1, R4121.2, U4109.1, U4112.1
XFD5706614908F1E1329B: U4129.6
XFE5AE10C500600BC9A46: U4115.4, U4133.9 (Q)
XFFE1FE953B93A0E1C890: R4166.1
