Takazudo/zudo-osc-hole-field/boards/osc-core/sheets/envelope_E2_K.kicad_sch

## KiCad design boards/osc-core/sheets/envelope_E2_K.kicad_sch (2026-10-05)

Schematic: envelope_E2_K.kicad_sch

Parts:
C4201: 1e-07 F; C0603; MPN GRM188R71H104KA93D
C4202: 1e-06 F; C0603
C4208: 1 µF; C0603
C4209: 1 nF C0G; C0603
C4210, C4213: 100 nF C0G; C1206; MPN 1206CG104J500NT; LCSC C46348
C4211, C4212: 1e-08 F; C0603
C4214, C4221, C4222, C4223, C4224, C4225, C4226, C4227, C4228, C4229, C4230, C4231, C4232, C4233, C4234, C4235, C4236, C4237, C4238, C4239, C4240, C4241, C4242, C4243, C4244, C4245, C4246, C4247, C4248, C4249, C4250, C4251, C4252, C4253, C4254, C4255, C4257, C4258, C4259, C4260, C4261, C4262, C4263, C4266, C4267, C4268, C4269, C4270, C4271: 100 nF; C0603; MPN GRM188R71H104KA93D
D4204: BAS16GW-QX; SOD-123; MPN BAS16GW-QX
D4205, D4206: BAT54S,215; SOT-23; MPN BAT54S,215
Q4201, Q4204: BCM847BS,115; SOT-363_SC-70-6; MPN BCM847BS,115
Q4202, Q4203, Q4205, Q4206: MMBT3906,215; SOT-23; MPN MMBT3906,215
R4201, R4202, R4219: 10000 Ω; R0603
R4203: 22000 Ω; R0603
R4204, R4217: 100000 Ω; R0603; MPN RT0603BRD07100KL
R4218: 33200 Ω; R0603
R4220: 390000 Ω; R0603
R4221: 4700 Ω; R0603
R4232, R4236, R4238, R4243, R4245, R4251, R4253, R4254, R4255, R4257, R4268, R4270, R4271, R4272, R4274, R4283, R4284, R4285, R4286, R4287, R4288, R4289, R4290: 100 kΩ; R0603; MPN RT0603BRD07100KL
R4233, R4234: 47 kΩ; R0603
R4235: 60 kΩ; R0603
R4237: 80 kΩ; R0603
R4239: 40 kΩ; R0603
R4240, R4256, R4273: 10 kΩ; R0603
R4241: 79 kΩ; R0603
R4242, R4262, R4263, R4279, R4280: 22 kΩ; R0603
R4244, R4246: 10 MΩ; R0603
R4247, R4248: 4.7 kΩ; R0603
R4249, R4266: 1000 Ω; R0603
R4250, R4267: 1e+07 Ω; R0603
R4252, R4258, R4269, R4275: 200 kΩ; R0603
R4259, R4276: 3.3 kΩ; R0603
R4260, R4265, R4277, R4282, R4292, R4294: 1 kΩ; R0603
R4261, R4278: 300 kΩ; R0603
R4264, R4281: 470 kΩ; R0603
R4291, R4293: 899 kΩ; R0603
R4295, R4296, R4297, R4298: 100 Ω; R0603
R4299: 64 kΩ; R0603
RB4201: 80 kΩ; R0603
RB4202, RB4203: 100 kΩ; R0603; MPN RT0603BRD07100KL
RB4204: 400 kΩ; R0603
RV4202, RV4206: 1 kΩ; Potentiometer_Bourns_TC33X_Vertical; MPN TC33X-2-102E
RV4203, RV4207: 50 kΩ; Potentiometer_Bourns_TC33X_Vertical
RV4204, RV4208: 10 kΩ; Potentiometer_Bourns_TC33X_Vertical; MPN TC33X-2-103E
U4201: REF5050AIDR; SOIC-8_3.9x4.9mm_P1.27mm; MPN REF5050AIDR; LCSC C27804
U4205: CD74HC221M96; SOIC-16_3.9x9.9mm_P1.27mm; MPN CD74HC221M96; LCSC C133954
U4206, U4208: ADG5412FBRUZ; TSSOP-16_4.4x5mm_P0.65mm; MPN ADG5412FBRUZ; LCSC C579073
U4207: LM13700M/NOPB; SOIC-16_3.9x9.9mm_P1.27mm; MPN LM13700M/NOPB; LCSC C1346265
U4209, U4210: LM393BIDR; SOIC-8_3.9x4.9mm_P1.27mm; MPN LM393BIDR
U4212: SN74HC14DR; SOIC-14_3.9x8.7mm_P1.27mm; MPN SN74HC14DR
U4213, U4214, U4215, U4216, U4217, U4218, U4219, U4220, U4221, U4222, U4223, U4224, U4225, U4226, U4227, U4228, U4229: SN74HC00DR; SOIC-14_3.9x8.7mm_P1.27mm; MPN SN74HC00DR
U4230, U4231, U4232, U4233, U4234, U4235, U4236, U4237, U4238: SN74HC74DR; SOIC-14_3.9x8.7mm_P1.27mm; MPN SN74HC74DR
U4239, U4240, U4241: OPA4197IPWR; TSSOP-14_4.4x5mm_P0.65mm; MPN OPA4197IPWR; LCSC C2057327
U4243, U4244, U4245: OPA4196IDR; SOIC-14_3.9x8.7mm_P1.27mm; MPN OPA4196IDR; LCSC C2057385

Connections:
+5V: C4221.1, C4230.1, C4231.1, C4232.1, C4233.1, C4234.1, C4235.1, C4236.1, C4237.1, C4238.1, C4239.1, C4240.1, C4241.1, C4242.1, C4243.1, C4244.1, C4245.1, C4246.1, C4247.1, C4248.1, C4249.1, C4250.1, C4251.1, C4252.1, C4253.1, C4254.1, C4255.1, C4257.1, D4204.1 (K), R4221.1, R4232.1, R4234.1, R4247.1, R4248.1, U4205.16 (VCC), U4212.14 (VCC), U4213.14 (VCC), U4214.14 (VCC), U4215.14 (VCC), U4216.14 (VCC), U4217.14 (VCC), U4218.14 (VCC), U4219.14 (VCC), U4220.14 (VCC), U4221.14 (VCC), U4222.14 (VCC), U4223.14 (VCC), U4224.14 (VCC), U4225.14 (VCC), U4226.14 (VCC), U4227.14 (VCC), U4228.14 (VCC), U4229.14 (VCC), U4230.2 (D), U4230.4 (~S), U4230.10 (~S), U4230.14 (VCC), U4231.4 (~S), U4231.10 (~S), U4231.14 (VCC), U4232.4 (~S), U4232.10 (~S), U4232.14 (VCC), U4233.4 (~S), U4233.10 (~S), U4233.14 (VCC), U4234.4 (~S), U4234.10 (~S), U4234.14 (VCC), U4235.4 (~S), U4235.10 (~S), U4235.14 (VCC), U4236.4 (~S), U4236.10 (~S), U4236.14 (VCC), U4237.4 (~S), U4237.10 (~S), U4237.14 (VCC), U4238.4 (~S), U4238.10 (~S), U4238.14 (VCC)
+12V: C4201.1, C4214.1, C4222.1, C4224.1, C4226.1, C4228.1, C4229.1, C4258.1, C4260.1, C4262.1, C4266.1, C4268.1, C4270.1, Q4202.2 (E), Q4203.2 (E), Q4205.2 (E), Q4206.2 (E), U4201.2 (Vin), U4206.13 (VDD), U4207.11 (V+), U4208.13 (VDD), U4209.8 (V+), U4210.8 (V+), U4239.4 (V+), U4240.4 (V+), U4241.4 (V+), U4243.4 (V+), U4244.4 (V+), U4245.4 (V+)
-12V: C4223.1, C4225.1, C4227.1, C4259.1, C4261.1, C4263.1, C4267.1, C4269.1, C4271.1, U4206.4 (VSS), U4207.6 (V-), U4208.4 (VSS), U4239.11 (V-), U4240.11 (V-), U4241.11 (V-), U4243.11 (V-), U4244.11 (V-), U4245.11 (V-)
AGND: C4201.2, C4202.2, C4208.2, C4209.2, C4211.2, C4212.2, C4213.2, C4214.2, C4221.2, C4222.2, C4223.2, C4224.2, C4225.2, C4226.2, C4227.2, C4228.2, C4229.2, C4230.2, C4231.2, C4232.2, C4233.2, C4234.2, C4235.2, C4236.2, C4237.2, C4238.2, C4239.2, C4240.2, C4241.2, C4242.2, C4243.2, C4244.2, C4245.2, C4246.2, C4247.2, C4248.2, C4249.2, C4250.2, C4251.2, C4252.2, C4253.2, C4254.2, C4255.2, C4257.2, C4258.2, C4259.2, C4260.2, C4261.2, C4262.2, C4263.2, C4266.2, C4267.2, C4268.2, C4269.2, C4270.2, C4271.2, D4205.1 (A), D4206.1 (A), Q4201.2 (B1), Q4204.2 (B1), R4204.2, R4236.2, R4238.2, R4240.2, R4242.2, R4250.2, R4265.2, R4267.2, R4282.2, R4284.2, R4290.2, R4292.2, R4294.2, RB4201.2, RB4204.2, U4201.4 (GND), U4205.1 (1A), U4205.8 (GND), U4205.9 (2A), U4205.10 (2B), U4205.11 (2R), U4206.5 (GND), U4207.7, U4207.10, U4208.5 (GND), U4208.6 (S4), U4208.7 (D4), U4208.8 (IN4), U4208.9 (IN3), U4208.10 (D3), U4208.11 (S3), U4208.15 (D2), U4209.4 (GND), U4210.4 (GND), U4210.5 (+), U4212.7 (GND), U4213.7 (GND), U4214.7 (GND), U4215.7 (GND), U4216.7 (GND), U4217.7 (GND), U4218.7 (GND), U4219.7 (GND), U4220.7 (GND), U4221.7 (GND), U4222.7 (GND), U4223.7 (GND), U4224.7 (GND), U4225.7 (GND), U4226.7 (GND), U4227.7 (GND), U4228.7 (GND), U4229.7 (GND), U4229.12, U4229.13, U4230.7 (GND), U4231.7 (GND), U4232.7 (GND), U4233.7 (GND), U4234.7 (GND), U4235.7 (GND), U4236.7 (GND), U4237.7 (GND), U4238.7 (GND), U4238.11 (C), U4238.12 (D), U4238.13 (~R), U4239.5 (+), U4240.10 (+), U4240.12 (+), U4241.3 (+), U4241.5 (+), U4241.12 (+), U4243.5 (+), U4243.10 (+), U4244.5 (+), U4244.10 (+), U4245.12 (+)
X0A84CA069600F8FD0B8B: R4253.1, R4254.1, U4243.7
X0DD9E04D4E84AB9D855B: U4212.10, U4226.2, U4234.12 (D)
X1A971D99E30F665B15CA: R4286.1, U4206.15 (D2), U4245.1
X1A4524A018E739A7C70C: R4276.2, RV4206.1 (CCW)
X1AC444A0F74CA23A6331: R4297.1, U4208.2 (D1)
X1DE536E250C70D71ECA8: R4295.1, U4207.5
X1ED287AA2323D684C490: R4233.1, U4212.8, U4230.3 (C), U4230.11 (C), U4231.3 (C), U4231.11 (C), U4232.3 (C), U4232.11 (C), U4233.3 (C), U4233.11 (C), U4234.3 (C), U4234.11 (C), U4235.3 (C), U4235.11 (C), U4236.3 (C), U4236.11 (C), U4237.3 (C), U4237.11 (C), U4238.3 (C)
X1FB0F3282A2906CC476D: U4205.3 (1R), U4222.9, U4225.4, U4226.12, U4230.9 (Q), U4231.1 (~R), U4231.13 (~R), U4232.1 (~R), U4232.13 (~R), U4233.1 (~R), U4233.13 (~R), U4234.1 (~R), U4234.13 (~R), U4235.1 (~R), U4235.13 (~R), U4236.1 (~R), U4236.13 (~R), U4237.1 (~R), U4237.13 (~R), U4238.1 (~R)
X2BEC6555C1BCBA4AE89D: U4216.9, U4217.12, U4220.12, U4224.10, U4226.1, U4226.13, U4229.4, U4229.5, U4236.9 (Q)
X02D12C14B0CAB1E7F718: R4201.2, R4202.2, U4239.6 (-)
X2D6211B37153A090F486: U4208.16 (IN2), U4225.11
X2E7775C1E830EADE8D41: R4217.2, R4218.2, U4209.2 (-)
X3B95FB5696077169BF93: U4214.13, U4234.6 (~Q)
X3B3546164215B8453756: R4291.2, R4292.1, U4207.3 (+)
X3C575293EAFE9EA70CF6: R4241.2, R4242.1, U4210.2 (-)
X3CABC8E08012FF73642A: U4221.11, U4222.2
X3F9340B957384731A232: U4218.3, U4219.5
X4BB9299EECC3D8621563: U4206.16 (IN2), U4228.3
X4C4DA0ECF7E21177000F: R4299.2, RB4201.1, U4245.10 (+)
X4D6F33A09A7070E535CC: U4220.3, U4220.5, U4221.2
X4E8652FEB1A87FF5532F: U4216.4, U4218.5, U4220.1, U4232.9 (Q)
X4FD83DE3CB5AF3744076: R4276.1, R4277.1, U4241.1
X5B63503F666168259C9D: U4212.6, U4230.1 (~R), U4230.13 (~R)
X5BD77B0AAD4F91073A2A: R4235.2, R4236.1, U4239.13 (-)
X5C6A0E78811335010D15: U4216.10, U4235.6 (~Q)
X5D4A53108DC1D28CFCB5: U4216.11, U4217.1
X5FA7D0A6648DCE1F5B04: U4218.8, U4218.12
X6A9FEEE94C58A0D53964: U4216.6, U4217.2, U4220.10
X6ABF7C254D133E2FA823: R4272.1, R4273.1, U4244.8
X6D8ABAD82B067961139B: R4254.2, R4255.2, U4243.9 (-)
X6DA95D10E0F071BB9B2B: Q4202.1 (B), Q4202.3 (C), Q4203.1 (B), R4262.1
X7C56254B1319CC3F06BE: U4213.12, U4236.8 (~Q)
X7CA77A345D0BC262664A: U4220.8, U4220.13
X7D10EC58B4AE517899E4: U4215.8, U4215.12
X7D234EE0D01DBA6A9DC0: U4218.6, U4218.9, U4218.10
X7D760147234197CDA29B: U4208.1 (IN1), U4226.6
X7E7EB1EA66AAB8FBD048: R4243.2, R4244.2, U4209.5 (+)
X7F03853AB7A77DCD3FB4: U4219.8, U4237.2 (D)
X9A343D229ADA66A13020: D4205.2 (K), D4206.2 (K), R4201.1, R4203.1, R4218.1, R4239.1, R4241.1, R4261.1, R4278.1, RB4202.1, RV4204.3 (CW), RV4208.3 (CW), U4210.6 (-), U4239.1, U4239.2 (-), U4239.12 (+), U4240.3 (+)
X9A2034E50FD04D6E119A: R4268.2, R4269.2, R4270.2, U4244.6 (-)
X9B2CDCE7F45C0332BF76: U4227.11, U4228.1, U4228.2
X09C75228E6C9D778023D: R4220.1, R4221.2, U4209.1, U4212.1
X9FEE4E35815B427B1A0F: U4228.6, U4228.9, U4228.10
X12A74203B09D8C450F8E: Q4204.6 (C1), RV4207.2 (Wiper), RV4207.3 (CW), U4241.6 (-)
X16A10D3CB234B2896841: R4246.1, R4248.2, U4210.1, U4212.13
X16DC783EBF02B248A046: C4212.1, R4266.2, R4267.1, U4244.3 (+)
X17D05E67CC19A656ED20: U4226.8, U4227.5, U4228.5
X20D51AE5172EDEA0477C: U4206.9 (IN3), U4228.8
X022F8A714E1F3BDF8B67: R4285.2, R4286.2, U4245.2 (-)
X23C6DCB4794CBF148F94: D4206.3 (COM), R4273.2, U4244.12 (+)
X26D101C21093AB3BDE3E: U4227.3, U4227.4, U4227.12
X31C9E24EF083958E74C0: U4215.6, U4215.9, U4215.10
X32C0C941B369867E8B33: R4288.1, U4240.6 (-), U4240.7
X32D5E22EA5A7EEA6FB61: D4205.3 (COM), R4256.2, U4243.12 (+)
X36CCB9FE455D58E44914: U4245.13 (-), U4245.14
X37A4CDF60CE76742ED58: R4280.2, U4207.16
X37F313A13CE25E3FCA70: U4205.2 (1B), U4238.5 (Q)
X37F2242FC836A63D2AFF: U4217.3, U4217.10
X39BA202F23934899FB36: U4206.1 (IN1), U4227.8
X39F92616021E1CBB70F6: U4223.6, U4223.9
X43C38A46059C2EC0FC00: R4271.2, R4272.2, U4244.9 (-)
X43FA9082F43CAA3CD5CC: R4252.1
X45B9C0D3605BA24BF3E9: U4228.11, U4229.1, U4229.2
X50CCAA357B64F996260A: R4278.2, RV4207.1 (CCW)
X51EDDB0D020EFD328585: U4221.8, U4221.12
X56A483E278A62BF9F396: R4264.2, R4265.1, U4207.4 (-)
X56CBB2094D914CFFDCF7: U4214.11, U4216.1
X60F94008649A67B7B9FA: U4214.6, U4214.9, U4214.10, U4225.5
X64AAB955F71387736A76: R4298.1, U4208.14 (S2)
X65D98BC0441C243E304B: U4218.11, U4219.1, U4219.2
X67EEFE349081BB113D97: U4226.3, U4226.5
X72E1BE83DC7BA46C155C: RB4202.2, RB4203.2, RB4204.1, U4245.9 (-)
X75D2ABF0A7F378737F46: U4223.8, U4223.12, U4223.13
X78A2BBD5F6A27E434495: U4225.8, U4225.12
X78BDC6ABACC4E8D7872D: U4205.4 (1Q), U4215.1, U4215.2
X78D3738DA5B80733B3D6: Q4201.5 (B2), R4260.2
X078D7758B3DCED56F9C9: R4287.2, R4288.2, U4245.5 (+)
X83FBF63F8C226B0DA1B2: U4222.6, U4237.12 (D)
X86B3EC30BF71E05044DD: U4221.3, U4221.13
X87BAE9878F4394C4CFC7: U4221.1, U4237.5 (Q)
X87EB8972925CDC4B1D2E: U4229.6
X89F49E3E32ED08466CA0: U4227.6, U4227.9, U4227.10
X91BB3C0DBC9CE600A94F: C4210.2, U4205.14 (1CX)
X94BBDBBFD497F64C9070: C4202.1, U4201.6 (Vout), U4239.3 (+)
X306BF9789069F2FAD454: U4220.6, U4220.9
X498DE6D8563260D00A21: R4217.1
X599DBF0D22154C7ABA30: U4223.2, U4236.5 (Q)
X633E5FD4C423E149AC96: R4274.2, R4275.2, RV4206.2 (Wiper), RV4206.3 (CW), U4241.2 (-)
X685F8079F40E68A51F67: U4216.3, U4217.4, U4217.5
X756F7DE1A2CA67408C88: Q4204.1 (E1), Q4204.4 (E2), U4241.7
X866F806A2C2EFFA52D6A: U4234.9 (Q), U4235.2 (D)
X871C17BAD7F4765C0590: R4274.1, U4244.13 (-), U4244.14
X905D3355FF030AC5B965: U4219.3, U4219.4
X1181CA2352DC36220A8E: U4217.11, U4218.2
X1593E7C543796CCEC30D: R4237.2, R4238.1, U4240.2 (-)
X1787E894A16B2B5FE18C: U4212.2, U4213.1, U4213.2
X2641C8E8B49F6542A0C7: U4233.5 (Q), U4233.12 (D)
X3114B5E129E661AF69AD: U4223.3, U4223.4, U4223.5
X3424E95A32BB77159B46: C4211.1, R4249.2, R4250.1, U4243.3 (+)
X6205F27FD127E9ECCBF4: U4213.6, U4213.10
X6257B42BA00AC8801A38: R4291.1, U4206.2 (D1), U4206.14 (S2)
X6598D7A6A04405CC9D96: U4224.1, U4224.4, U4224.5
X6913EF43602D5256AD58: U4217.8, U4236.12 (D)
X6971D913D0096F4F900D: R4251.2, R4252.2, R4253.2, U4243.6 (-)
X7958C76AAF883E55ECFD: U4215.3, U4215.13
X8518DC54BB1633670979: Q4201.3 (C2), R4262.2
X8762C47650553C93BFD1: R4219.2, R4220.2, U4209.3 (+)
X9684F2DFEE52F3039A10: R4235.1, U4208.3 (S1), U4239.14
X10852B4E217E1D395843: R4285.1, R4287.1, R4299.1, U4241.8, U4241.9 (-)
X12194F2AB1F3DE1EBE32: Q4204.3 (C2), R4279.2
X12994C830C6B9AF773BF: U4213.11, U4214.1, U4214.2
X17164D9184653CD452EA: R4259.1, R4260.1, U4240.8
X21790F30A6FA0B62F7C5: U4222.11, U4223.1, U4228.4, U4228.12
X23089EE03A9496FEB9EF: U4224.6, U4224.9
X39321C631C2774C4B07E: U4230.5 (Q), U4230.12 (D)
X46136FB7BCB8B65FDDB2: R4296.1, U4207.12
X55481DF6E8E80C88A988: U4222.3, U4222.4, U4222.5
X57483F724E5DFE9DDED4: U4226.11, U4227.1, U4227.2
X59588C7C0A606038D597: R4281.2, R4282.1, U4207.14 (+)
X594671D4E0DDE8EDD9FF: U4233.2 (D)
X805727E2C51303089409: R4239.2, R4240.1, U4240.5 (+)
X856506E692F4E43127E6: Q4205.1 (B), Q4205.3 (C), Q4206.1 (B), R4279.1
X2962895DC9EE122A86A7: R4261.2, RV4203.1 (CCW)
X6854898EE6CD6B1E9DE9: R4202.1, R4258.1, R4275.1, RV4204.1 (CCW), RV4208.1 (CCW), U4239.7
X54642202DBD24BC1DA25: U4217.13, U4220.4, U4235.5 (Q)
X91567126C8B0151D3BA2: U4214.12, U4218.13, U4220.2, U4231.9 (Q), U4234.2 (D)
XA5F63E36B74FA8DB5753: U4212.4, U4212.5
XA44C5C0E55C9EA7BDC47: U4222.8, U4222.12, U4222.13
XA277A8A41DD6170FBD7D: R4251.1, U4243.1, U4243.2 (-)
XA3602BDD578351FD5DD6: U4224.3, U4224.12
XAAF00CCA5FF4D85D61E4: U4213.13, U4218.1, U4226.4, U4237.6 (~Q)
XAEEDE630CD20C04E853C: U4217.6, U4217.9, U4218.4, U4222.1, U4223.10
XAFA8F77E6E3BCF7068D3: U4216.8, U4216.12, U4216.13
XAFB594C53DCECA3A3AD4: R4269.1
XAFD47ABDBFD64823F95B: U4224.8, U4224.13
XB0BE9F5A801357F02E53: R4281.1, RV4208.2 (Wiper)
XB6D358388979575E9048: C4209.1, R4233.2, U4212.9
XB8D83C764066FEA571D7: U4229.8
XB398B577DEF067D2939B: U4235.9 (Q), U4236.2 (D)
XB636DC05CE60165FFA3F: Q4203.3 (C), R4263.1
XB6126EF3BD713ABCAC1E: U4219.13, U4236.6 (~Q)
XBB515FF163B4FB1302E7: U4225.6, U4225.9, U4225.10
XBC74706F69BBC78AD976: Q4201.6 (C1), RV4203.2 (Wiper), RV4203.3 (CW), U4240.13 (-)
XBC7436928D2CB9206C4C: U4216.5, U4231.8 (~Q)
XBF75B9C71B17FA61D8C7: U4215.11, U4216.2
XC7A38D4E46204BAB5AC4: R4293.1, U4206.6 (S4), U4206.11 (S3)
XC8DAA9AE1381392EAE63: U4214.5, U4237.8 (~Q)
XC8E2FD11DD3EAB64FCCA: C4208.1, D4204.2 (A), R4232.2, U4212.3
XC22FB55511DF5FFC558F: R4257.2, R4258.2, RV4202.2 (Wiper), RV4202.3 (CW), U4240.9 (-)
XC57F7B82CBD19A62D640: R4249.1
XC2783744DE58877C1FBF: U4223.11, U4238.2 (D)
XC80414462F4FED94A56A: U4220.11, U4221.5
XCB3543D1B4571EB23CA5: R4245.2, R4246.2, U4210.3 (+)
XCC667F25662CC0A86294: U4226.9, U4226.10, U4227.13, U4228.13
XCD73253CE48AB875471C: U4213.4, U4213.5
XCF51DC1A20A4303C8D8F: R4293.2, R4294.1, U4207.13 (-)
XCFDB8030594DCB3A26BA: U4219.12, U4222.10, U4224.2, U4225.1, U4229.9, U4229.10, U4237.9 (Q)
XD0FD12BFFC4BB6DC6FBF: C4210.1, R4234.2, U4205.15 (1RXCX)
XD2CD8F2DD019093785A4: U4224.11
XD985B5822EA5075CFAD2: U4221.6, U4221.9, U4221.10
XD1659AD85AEF1B22ED6F: R4259.2, RV4202.1 (CCW)
XD9992CFFE3B9C146B5E5: R4237.1, R4243.1, R4283.1, U4206.3 (S1), U4206.10 (D3), U4240.1
XDA3FC00130719CE50C26: R4270.1, R4271.1, U4244.7
XDA92ACB3EF12CE3F3886: R4263.2, U4207.1
XDBF046816E8B85B46B1A: U4213.8, U4231.2 (D)
XDCC3D1898F24E0CBE8EB: C4213.1, R4295.2, R4296.2, R4297.2, R4298.2, U4241.10 (+)
XDDF350AC45C70DE039EC: R4255.1, R4256.1, U4243.8
XDFADF19BB2B249706894: U4241.13 (-), U4241.14
XE9E155A1ECAC8FB5DDDB: U4219.6, U4219.9, U4219.10
XE28AE84662697FA0D99F: U4212.12, U4225.2, U4235.12 (D)
XE50F7010B563D9E69D06: R4266.1
XE361E3D9C4F578926787: R4203.2, R4204.1, U4239.10 (+)
XE6036FEDB0A1BFA311BC: R4283.2, R4284.1, U4245.3 (+)
XE9385F6BDD94FFEEA4BD: U4214.3, U4214.4
XEB7A58E2BBA1ACD3E0C0: U4225.3, U4225.13
XEBAE7E4F7360E48BBC9E: U4232.5 (Q), U4232.12 (D)
XEBD42A167753CD6F1F23: U4232.2 (D)
XEC7EFFA422D3AB30646B: Q4204.5 (B2), R4277.2
XECA258C8ED3E4777ACE3: R4219.1, U4239.8, U4239.9 (-)
XED05C71AF04E590894E2: R4264.1, RV4204.2 (Wiper)
XF1A55B3DB202A4F3D0F0: Q4206.3 (C), R4280.1
XF1A64A507952C86C8B6C: U4213.3, U4213.9
XF2A31DA543815EB75054: R4244.1, R4247.2, U4209.7, U4212.11
XF4F21BF06172AE0DE2B1: U4214.8, U4215.5
XF691FA0FCF8D66AE54E9: Q4201.1 (E1), Q4201.4 (E2), U4240.14
XF766C9ADC76978AE5E08: U4215.4, U4233.9 (Q)
XF017899C98E79B0137BB: R4245.1, R4289.1, U4206.7 (D4), U4209.6 (-), U4245.7
XFA006B7032088BE1400E: R4289.2, R4290.1, U4245.6 (-)
XFC767A6D9E59DD871AAE: U4231.5 (Q), U4231.12 (D)
XFC63993F7EA30E80F658: R4268.1, U4244.1, U4244.2 (-)
XFD6D3BC4F6CA8CDDDA78: RB4203.1, U4245.8
XFEED735F75B4AF9E6F26: U4206.8 (IN4), U4229.3
XFF66AD386DD145E74B5F: R4257.1, U4243.13 (-), U4243.14
XFF454C445116C1394A4D: U4219.11, U4221.4
