Takazudo/zudo-osc-hole-field/boards/osc-core/sheets/envelope_E3_K.kicad_sch

## KiCad design boards/osc-core/sheets/envelope_E3_K.kicad_sch (2026-10-05)

Schematic: envelope_E3_K.kicad_sch

Parts:
C4301: 1e-07 F; C0603; MPN GRM188R71H104KA93D
C4302: 1e-06 F; C0603
C4308: 1 µF; C0603
C4309: 1 nF C0G; C0603
C4310, C4313: 100 nF C0G; C1206; MPN 1206CG104J500NT; LCSC C46348
C4311, C4312: 1e-08 F; C0603
C4314, C4321, C4322, C4323, C4324, C4325, C4326, C4327, C4328, C4329, C4330, C4331, C4332, C4333, C4334, C4335, C4336, C4337, C4338, C4339, C4340, C4341, C4342, C4343, C4344, C4345, C4346, C4347, C4348, C4349, C4350, C4351, C4352, C4353, C4354, C4355, C4357, C4358, C4359, C4360, C4361, C4362, C4363, C4366, C4367, C4368, C4369, C4370, C4371: 100 nF; C0603; MPN GRM188R71H104KA93D
D4304: BAS16GW-QX; SOD-123; MPN BAS16GW-QX
D4305, D4306: BAT54S,215; SOT-23; MPN BAT54S,215
Q4301, Q4304: BCM847BS,115; SOT-363_SC-70-6; MPN BCM847BS,115
Q4302, Q4303, Q4305, Q4306: MMBT3906,215; SOT-23; MPN MMBT3906,215
R4301, R4302, R4319: 10000 Ω; R0603
R4303: 22000 Ω; R0603
R4304, R4317: 100000 Ω; R0603; MPN RT0603BRD07100KL
R4318: 33200 Ω; R0603
R4320: 390000 Ω; R0603
R4321: 4700 Ω; R0603
R4332, R4336, R4338, R4343, R4345, R4351, R4353, R4354, R4355, R4357, R4368, R4370, R4371, R4372, R4374, R4383, R4384, R4385, R4386, R4387, R4388, R4389, R4390: 100 kΩ; R0603; MPN RT0603BRD07100KL
R4333, R4334: 47 kΩ; R0603
R4335: 60 kΩ; R0603
R4337: 80 kΩ; R0603
R4339: 40 kΩ; R0603
R4340, R4356, R4373: 10 kΩ; R0603
R4341: 79 kΩ; R0603
R4342, R4362, R4363, R4379, R4380: 22 kΩ; R0603
R4344, R4346: 10 MΩ; R0603
R4347, R4348: 4.7 kΩ; R0603
R4349, R4366: 1000 Ω; R0603
R4350, R4367: 1e+07 Ω; R0603
R4352, R4358, R4369, R4375: 200 kΩ; R0603
R4359, R4376: 3.3 kΩ; R0603
R4360, R4365, R4377, R4382, R4392, R4394: 1 kΩ; R0603
R4361, R4378: 300 kΩ; R0603
R4364, R4381: 470 kΩ; R0603
R4391, R4393: 899 kΩ; R0603
R4395, R4396, R4397, R4398: 100 Ω; R0603
R4399: 64 kΩ; R0603
RB4301: 80 kΩ; R0603
RB4302, RB4303: 100 kΩ; R0603; MPN RT0603BRD07100KL
RB4304: 400 kΩ; R0603
RV4302, RV4306: 1 kΩ; Potentiometer_Bourns_TC33X_Vertical; MPN TC33X-2-102E
RV4303, RV4307: 50 kΩ; Potentiometer_Bourns_TC33X_Vertical
RV4304, RV4308: 10 kΩ; Potentiometer_Bourns_TC33X_Vertical; MPN TC33X-2-103E
U4301: REF5050AIDR; SOIC-8_3.9x4.9mm_P1.27mm; MPN REF5050AIDR; LCSC C27804
U4305: CD74HC221M96; SOIC-16_3.9x9.9mm_P1.27mm; MPN CD74HC221M96; LCSC C133954
U4306, U4308: ADG5412FBRUZ; TSSOP-16_4.4x5mm_P0.65mm; MPN ADG5412FBRUZ; LCSC C579073
U4307: LM13700M/NOPB; SOIC-16_3.9x9.9mm_P1.27mm; MPN LM13700M/NOPB; LCSC C1346265
U4309, U4310: LM393BIDR; SOIC-8_3.9x4.9mm_P1.27mm; MPN LM393BIDR
U4312: SN74HC14DR; SOIC-14_3.9x8.7mm_P1.27mm; MPN SN74HC14DR
U4313, U4314, U4315, U4316, U4317, U4318, U4319, U4320, U4321, U4322, U4323, U4324, U4325, U4326, U4327, U4328, U4329: SN74HC00DR; SOIC-14_3.9x8.7mm_P1.27mm; MPN SN74HC00DR
U4330, U4331, U4332, U4333, U4334, U4335, U4336, U4337, U4338: SN74HC74DR; SOIC-14_3.9x8.7mm_P1.27mm; MPN SN74HC74DR
U4339, U4340, U4341: OPA4197IPWR; TSSOP-14_4.4x5mm_P0.65mm; MPN OPA4197IPWR; LCSC C2057327
U4343, U4344, U4345: OPA4196IDR; SOIC-14_3.9x8.7mm_P1.27mm; MPN OPA4196IDR; LCSC C2057385

Connections:
+5V: C4321.1, C4330.1, C4331.1, C4332.1, C4333.1, C4334.1, C4335.1, C4336.1, C4337.1, C4338.1, C4339.1, C4340.1, C4341.1, C4342.1, C4343.1, C4344.1, C4345.1, C4346.1, C4347.1, C4348.1, C4349.1, C4350.1, C4351.1, C4352.1, C4353.1, C4354.1, C4355.1, C4357.1, D4304.1 (K), R4321.1, R4332.1, R4334.1, R4347.1, R4348.1, U4305.16 (VCC), U4312.14 (VCC), U4313.14 (VCC), U4314.14 (VCC), U4315.14 (VCC), U4316.14 (VCC), U4317.14 (VCC), U4318.14 (VCC), U4319.14 (VCC), U4320.14 (VCC), U4321.14 (VCC), U4322.14 (VCC), U4323.14 (VCC), U4324.14 (VCC), U4325.14 (VCC), U4326.14 (VCC), U4327.14 (VCC), U4328.14 (VCC), U4329.14 (VCC), U4330.2 (D), U4330.4 (~S), U4330.10 (~S), U4330.14 (VCC), U4331.4 (~S), U4331.10 (~S), U4331.14 (VCC), U4332.4 (~S), U4332.10 (~S), U4332.14 (VCC), U4333.4 (~S), U4333.10 (~S), U4333.14 (VCC), U4334.4 (~S), U4334.10 (~S), U4334.14 (VCC), U4335.4 (~S), U4335.10 (~S), U4335.14 (VCC), U4336.4 (~S), U4336.10 (~S), U4336.14 (VCC), U4337.4 (~S), U4337.10 (~S), U4337.14 (VCC), U4338.4 (~S), U4338.10 (~S), U4338.14 (VCC)
+12V: C4301.1, C4314.1, C4322.1, C4324.1, C4326.1, C4328.1, C4329.1, C4358.1, C4360.1, C4362.1, C4366.1, C4368.1, C4370.1, Q4302.2 (E), Q4303.2 (E), Q4305.2 (E), Q4306.2 (E), U4301.2 (Vin), U4306.13 (VDD), U4307.11 (V+), U4308.13 (VDD), U4309.8 (V+), U4310.8 (V+), U4339.4 (V+), U4340.4 (V+), U4341.4 (V+), U4343.4 (V+), U4344.4 (V+), U4345.4 (V+)
-12V: C4323.1, C4325.1, C4327.1, C4359.1, C4361.1, C4363.1, C4367.1, C4369.1, C4371.1, U4306.4 (VSS), U4307.6 (V-), U4308.4 (VSS), U4339.11 (V-), U4340.11 (V-), U4341.11 (V-), U4343.11 (V-), U4344.11 (V-), U4345.11 (V-)
AGND: C4301.2, C4302.2, C4308.2, C4309.2, C4311.2, C4312.2, C4313.2, C4314.2, C4321.2, C4322.2, C4323.2, C4324.2, C4325.2, C4326.2, C4327.2, C4328.2, C4329.2, C4330.2, C4331.2, C4332.2, C4333.2, C4334.2, C4335.2, C4336.2, C4337.2, C4338.2, C4339.2, C4340.2, C4341.2, C4342.2, C4343.2, C4344.2, C4345.2, C4346.2, C4347.2, C4348.2, C4349.2, C4350.2, C4351.2, C4352.2, C4353.2, C4354.2, C4355.2, C4357.2, C4358.2, C4359.2, C4360.2, C4361.2, C4362.2, C4363.2, C4366.2, C4367.2, C4368.2, C4369.2, C4370.2, C4371.2, D4305.1 (A), D4306.1 (A), Q4301.2 (B1), Q4304.2 (B1), R4304.2, R4336.2, R4338.2, R4340.2, R4342.2, R4350.2, R4365.2, R4367.2, R4382.2, R4384.2, R4390.2, R4392.2, R4394.2, RB4301.2, RB4304.2, U4301.4 (GND), U4305.1 (1A), U4305.8 (GND), U4305.9 (2A), U4305.10 (2B), U4305.11 (2R), U4306.5 (GND), U4307.7, U4307.10, U4308.5 (GND), U4308.6 (S4), U4308.7 (D4), U4308.8 (IN4), U4308.9 (IN3), U4308.10 (D3), U4308.11 (S3), U4308.15 (D2), U4309.4 (GND), U4310.4 (GND), U4310.5 (+), U4312.7 (GND), U4313.7 (GND), U4314.7 (GND), U4315.7 (GND), U4316.7 (GND), U4317.7 (GND), U4318.7 (GND), U4319.7 (GND), U4320.7 (GND), U4321.7 (GND), U4322.7 (GND), U4323.7 (GND), U4324.7 (GND), U4325.7 (GND), U4326.7 (GND), U4327.7 (GND), U4328.7 (GND), U4329.7 (GND), U4329.12, U4329.13, U4330.7 (GND), U4331.7 (GND), U4332.7 (GND), U4333.7 (GND), U4334.7 (GND), U4335.7 (GND), U4336.7 (GND), U4337.7 (GND), U4338.7 (GND), U4338.11 (C), U4338.12 (D), U4338.13 (~R), U4339.5 (+), U4340.10 (+), U4340.12 (+), U4341.3 (+), U4341.5 (+), U4341.12 (+), U4343.5 (+), U4343.10 (+), U4344.5 (+), U4344.10 (+), U4345.12 (+)
X0CA2592C81E474A27AC8: U4326.11, U4327.1, U4327.2
X0D7C50C0CBA5879D2AD4: R4383.2, R4384.1, U4345.3 (+)
X0FA9D6971A52E4C694DE: U4327.6, U4327.9, U4327.10
X01A05DBEFB68471D9824: U4324.1, U4324.4, U4324.5
X1BBA3C5B996B98DC88F4: U4329.8
X1CAC450A55357ADE51F9: R4335.1, U4308.3 (S1), U4339.14
X1DE69D6B53FAC006B0F4: Q4304.3 (C2), R4379.2
X2A539FE5C68A9F37A24E: U4319.11, U4321.4
X2AECC2B60FC708AF2753: RB4302.2, RB4303.2, RB4304.1, U4345.9 (-)
X2B7DA31306B531910B54: R4363.2, U4307.1
X2CD81BDCB25C8DF0A439: C4312.1, R4366.2, R4367.1, U4344.3 (+)
X3B8BA61DD852C09F9593: R4349.1
X3CCC68305A4889E5B739: R4343.2, R4344.2, U4309.5 (+)
X3EA8F03F93EFE830FD24: U4321.8, U4321.12
X3F0A69380D7AFCECF3E9: U4327.3, U4327.4, U4327.12
X03FD5B87564EFF1FF6E1: R4371.2, R4372.2, U4344.9 (-)
X3FE29A6989827DF6157E: U4316.5, U4331.8 (~Q)
X4DE27BACA30E9244C5AA: R4387.2, R4388.2, U4345.5 (+)
X5A64B6B642AEA36F8EEF: Q4304.1 (E1), Q4304.4 (E2), U4341.7
X5C8C12699DA656C04486: U4314.11, U4316.1
X5CA79EEE9C51F0172EE9: U4322.11, U4323.1, U4328.4, U4328.12
X5CDFE315C31033F695D9: R4364.1, RV4304.2 (Wiper)
X5DB63D4D272C1EDEBF44: U4325.8, U4325.12
X5E11D4E5DF2B9813D24F: U4313.13, U4318.1, U4326.4, U4337.6 (~Q)
X5F28F717C34A7930E4C4: R4368.1, U4344.1, U4344.2 (-)
X5FDA566A5159A8966077: U4332.5 (Q), U4332.12 (D)
X6C885940F0F29560C21C: U4322.8, U4322.12, U4322.13
X6DBFAB1B234789E0086E: U4305.2 (1B), U4338.5 (Q)
X6EAB4E24C36DA2052427: U4308.1 (IN1), U4326.6
X6F1627815CB83B484C21: Q4302.1 (B), Q4302.3 (C), Q4303.1 (B), R4362.1
X7BBA7B22406F0D0DD1F3: C4310.2, U4305.14 (1CX)
X7C649B11D66500924F09: Q4301.6 (C1), RV4303.2 (Wiper), RV4303.3 (CW), U4340.13 (-)
X7DC20A7C73DBAB9D2D44: R4388.1, U4340.6 (-), U4340.7
X7E45A046FB782CA910F4: U4308.16 (IN2), U4325.11
X8A939B676B6F87E5F9A3: R4385.1, R4387.1, R4399.1, U4341.8, U4341.9 (-)
X8AD2BEB1C9E4FA00E26C: U4315.6, U4315.9, U4315.10
X8BB6F11711C26B736BD1: U4316.6, U4317.2, U4320.10
X8C0B71408D8A5862CD1C: U4319.13, U4336.6 (~Q)
X8CD8AAA9269108B29A3E: R4378.2, RV4307.1 (CCW)
X8D4AF69F7189A36FD4DE: U4306.8 (IN4), U4329.3
X9A93297CD6D5A3C0028A: R4357.2, R4358.2, RV4302.2 (Wiper), RV4302.3 (CW), U4340.9 (-)
X9D97DEEB1AEAC747CB2C: R4320.1, R4321.2, U4309.1, U4312.1
X9DEB5F001A0D5A1FF847: U4314.8, U4315.5
X9EFA1C871642BFE1B108: R4374.1, U4344.13 (-), U4344.14
X9F57A0A3515A58A6A21F: U4313.3, U4313.9
X10E69CCE15DFD7BBE677: U4312.12, U4325.2, U4335.12 (D)
X15C8C0250F11999D7D0F: U4319.3, U4319.4
X20EC70FBFE043CC5CEB0: U4314.5, U4337.8 (~Q)
X24D1E35BE53EEF488858: C4310.1, R4334.2, U4305.15 (1RXCX)
X29F25AF61EEC48549BC9: U4330.5 (Q), U4330.12 (D)
X35C328C82C2EDBE601ED: R4366.1
X49F97780E6B834EEAA85: U4322.6, U4337.12 (D)
X52D8CE85FCB5583D4724: U4316.3, U4317.4, U4317.5
X52D3942E9E743BB408A0: U4318.8, U4318.12
X55E839F84542C73DAED0: U4315.3, U4315.13
X58B2621145471EFE082D: U4306.9 (IN3), U4328.8
X59FBA17EF0ED74FF9324: U4305.4 (1Q), U4315.1, U4315.2
X64E031F34BD230441284: U4312.6, U4330.1 (~R), U4330.13 (~R)
X65E9ACD836207CB772F0: U4328.11, U4329.1, U4329.2
X67F346A0D79DF6F75593: R4344.1, R4347.2, U4309.7, U4312.11
X68FD85AA3DBB4BEA3FBE: R4389.2, R4390.1, U4345.6 (-)
X069C51FDD213E58EC684: U4312.10, U4326.2, U4334.12 (D)
X69F956D2CD0D8F7D7812: D4305.2 (K), D4306.2 (K), R4301.1, R4303.1, R4318.1, R4339.1, R4341.1, R4361.1, R4378.1, RB4302.1, RV4304.3 (CW), RV4308.3 (CW), U4310.6 (-), U4339.1, U4339.2 (-), U4339.12 (+), U4340.3 (+)
X73AC3F41ED499F592269: U4320.8, U4320.13
X73BFF624F35D4FC643CB: U4318.3, U4319.5
X87BD7E2A95BB48CC9CA2: U4312.4, U4312.5
X89D638F5278CCCF01C15: R4346.1, R4348.2, U4310.1, U4312.13
X94DC3D6E6D0768A448EC: U4315.8, U4315.12
X0113E48F2FDEB4144647: U4324.3, U4324.12
X130E2D2473EEC58833A8: U4333.2 (D)
X236E8A3CF618A445526F: U4326.3, U4326.5
X271FBCF21B90956B8B33: R4317.2, R4318.2, U4309.2 (-)
X0322A96994D0F6150CC7: R4337.2, R4338.1, U4340.2 (-)
X0378AD2C65B9A8B5DD60: Q4304.6 (C1), RV4307.2 (Wiper), RV4307.3 (CW), U4341.6 (-)
X401A3E28D0ECB2D55197: U4316.9, U4317.12, U4320.12, U4324.10, U4326.1, U4326.13, U4329.4, U4329.5, U4336.9 (Q)
X514A1A101C58783C4732: U4320.3, U4320.5, U4321.2
X671D5CF0AD1EC723E326: U4314.13, U4334.6 (~Q)
X686EA0EB03FEEE1E85B5: R4357.1, U4343.13 (-), U4343.14
X812A873D57C4105D737C: U4317.11, U4318.2
X816C8E3CEACE630E06C0: U4306.16 (IN2), U4328.3
X899EA6E70B204D2F2C06: R4391.1, U4306.2 (D1), U4306.14 (S2)
X997DC82E1ED6194854F5: U4321.1, U4337.5 (Q)
X1082D620E6E048599FF7: U4335.9 (Q), U4336.2 (D)
X1292CA2B66716A2AA242: R4368.2, R4369.2, R4370.2, U4344.6 (-)
X1700D53D113B9FE47CB8: R4386.1, U4306.15 (D2), U4345.1
X01805B1B557771ADFAE3: U4315.11, U4316.2
X1943D2950116BF81C66A: U4328.6, U4328.9, U4328.10
X3162B89648E924CF513D: R4396.1, U4307.12
X3349DDAF66526EFAFF34: U4321.6, U4321.9, U4321.10
X4701B2E18BA5AA82541A: U4314.3, U4314.4
X5055C27981BDF0614633: C4309.1, R4333.2, U4312.9
X6944ADF93ED14D03649E: R4376.2, RV4306.1 (CCW)
X8801FA94C18BF6DCE706: R4301.2, R4302.2, U4339.6 (-)
X12047C08E3789BF3D698: R4370.1, R4371.1, U4344.7
X21241E7FE0932E6FEB0B: R4364.2, R4365.1, U4307.4 (-)
X36050CF715245F031E2A: R4380.2, U4307.16
X39239E40C86508601CCC: Q4301.1 (E1), Q4301.4 (E2), U4340.14
X55778DC605F2ECD44CA9: Q4304.5 (B2), R4377.2
X63613ECE89F282A509B6: U4329.6
X80056FC95C0254B6B19D: U4345.13 (-), U4345.14
X170958AA405357DF2A72: C4302.1, U4301.6 (Vout), U4339.3 (+)
X312086F4F78571DECDD5: U4305.3 (1R), U4322.9, U4325.4, U4326.12, U4330.9 (Q), U4331.1 (~R), U4331.13 (~R), U4332.1 (~R), U4332.13 (~R), U4333.1 (~R), U4333.13 (~R), U4334.1 (~R), U4334.13 (~R), U4335.1 (~R), U4335.13 (~R), U4336.1 (~R), U4336.13 (~R), U4337.1 (~R), U4337.13 (~R), U4338.1 (~R)
X477869C5EB272DECFBFA: R4339.2, R4340.1, U4340.5 (+)
X753870F9D5335867C49C: U4316.8, U4316.12, U4316.13
X947670BE069068E55EBF: U4317.8, U4336.12 (D)
X948632D591C37A12443D: U4317.13, U4320.4, U4335.5 (Q)
X3668062C60F3366737E4: R4398.1, U4308.14 (S2)
X6012073DA8F01B869B3F: R4352.1
X485784499A3F231C8130: U4313.11, U4314.1, U4314.2
XA0A1289E57FBAB2B3CBB: U4320.6, U4320.9
XA5C9523048D0E965BEEB: U4313.6, U4313.10
XA26D13D3F80A17F498E1: R4393.1, U4306.6 (S4), U4306.11 (S3)
XA8829B6F08F45015B00C: C4313.1, R4395.2, R4396.2, R4397.2, R4398.2, U4341.10 (+)
XA92686FC9F41649DE2A6: R4317.1
XAA2B21CE6933CF45701D: R4381.1, RV4308.2 (Wiper)
XAA3818811D5228BF0588: U4334.9 (Q), U4335.2 (D)
XACF244F434C21A2D7699: R4395.1, U4307.5
XAFA7B83AE73642D2CEA8: U4333.5 (Q), U4333.12 (D)
XAFAB4B26EDBCD752DEA4: U4327.11, U4328.1, U4328.2
XAFB17B4E6525CF728286: Q4306.3 (C), R4380.1
XB03C51412136D6EFCB85: R4337.1, R4343.1, R4383.1, U4306.3 (S1), U4306.10 (D3), U4340.1
XB4DB5DD4DC2F166D2AA2: R4303.2, R4304.1, U4339.10 (+)
XB5F8ADEEF834D3B4CBAD: U4321.11, U4322.2
XB06DFEFEEC794FD6A87E: U4316.10, U4335.6 (~Q)
XB6E30AE72082400C5E87: U4316.4, U4318.5, U4320.1, U4332.9 (Q)
XB8F6BD5142987A0CD439: U4321.3, U4321.13
XB28FA53CC1E9A761BD1C: U4313.4, U4313.5
XB44EFAA1194BEDE349E0: R4385.2, R4386.2, U4345.2 (-)
XB52CB89C2AC1B41F5B1A: RB4303.1, U4345.8
XB76A096403B6FFEA9B3A: Q4301.3 (C2), R4362.2
XB2331C657A1370BC6C0D: U4324.8, U4324.13
XB4655976C2CCAF650BAA: U4318.11, U4319.1, U4319.2
XBC7B78FF6723B01D66F1: U4319.12, U4322.10, U4324.2, U4325.1, U4329.9, U4329.10, U4337.9 (Q)
XBED713F0F20C2BEF6433: R4369.1
XBF1D8FB56DA398292EB0: U4312.2, U4313.1, U4313.2
XBF19F024027D969129D7: U4318.6, U4318.9, U4318.10
XC2EF68D5C63E11500E03: Q4303.3 (C), R4363.1
XC3D04DC0A953CEA77C49: C4308.1, D4304.2 (A), R4332.2, U4312.3
XC6C501BDB81F8BF753BA: R4399.2, RB4301.1, U4345.10 (+)
XC9BD86D4940BDBE42C0B: R4335.2, R4336.1, U4339.13 (-)
XC27C7485F486DCBB47BD: U4314.6, U4314.9, U4314.10, U4325.5
XC44E2C753F6783E0975C: U4331.5 (Q), U4331.12 (D)
XC50B7829A9B3F3E3CDDB: R4345.1, R4389.1, U4306.7 (D4), U4309.6 (-), U4345.7
XC0102DFCC1BE40DC0DD0: U4323.6, U4323.9
XC394C67B39CCAC7BCAC2: U4332.2 (D)
XC7620063D6932988160F: R4345.2, R4346.2, U4310.3 (+)
XC392958081805884093F: R4355.1, R4356.1, U4343.8
XCA7CE3945CD687FC27E9: U4313.12, U4336.8 (~Q)
XCCBF83DEFA06178F456E: U4341.13 (-), U4341.14
XCD15CE99A6C452D262EE: U4317.6, U4317.9, U4318.4, U4322.1, U4323.10
XCFC3683CB20E7CB826A4: R4351.1, U4343.1, U4343.2 (-)
XD2BF02344E6D80A55C60: R4372.1, R4373.1, U4344.8
XD4FFDFD830CE782DA643: R4351.2, R4352.2, R4353.2, U4343.6 (-)
XD5CF8062D9EA8F43FF47: D4306.3 (COM), R4373.2, U4344.12 (+)
XD7E84B329630A4D19EE1: U4313.8, U4331.2 (D)
XD14B79679D8055F377ED: U4323.8, U4323.12, U4323.13
XD30D64D870AD5995FE06: U4316.11, U4317.1
XD48B778961D2616D8031: U4317.3, U4317.10
XD925A488BFF88EC55A0E: U4326.9, U4326.10, U4327.13, U4328.13
XD6088B4417EFCFCD3803: R4376.1, R4377.1, U4341.1
XD21480E64CC3B0CC1CAF: Q4301.5 (B2), R4360.2
XD8001988DC3FA5FEB506: U4326.8, U4327.5, U4328.5
XD85490673C6A6886B2E4: U4320.11, U4321.5
XDA5781E448273B3A34F5: R4361.2, RV4303.1 (CCW)
XDCBBA1CDA691270F301B: R4397.1, U4308.2 (D1)
XDD0A879AAE0468206992: U4319.6, U4319.9, U4319.10
XDE32C496AC71F9F9E6D3: R4341.2, R4342.1, U4310.2 (-)
XE3F3699CF0443CED4962: U4323.3, U4323.4, U4323.5
XE4CCF1D56CCCC049890A: R4333.1, U4312.8, U4330.3 (C), U4330.11 (C), U4331.3 (C), U4331.11 (C), U4332.3 (C), U4332.11 (C), U4333.3 (C), U4333.11 (C), U4334.3 (C), U4334.11 (C), U4335.3 (C), U4335.11 (C), U4336.3 (C), U4336.11 (C), U4337.3 (C), U4337.11 (C), U4338.3 (C)
XE7A834E04C0A4D56CB8B: U4306.1 (IN1), U4327.8
XE8F166A76F8764B91063: U4322.3, U4322.4, U4322.5
XE14B8B11FD282F26CE7E: Q4305.1 (B), Q4305.3 (C), Q4306.1 (B), R4379.1
XE24EDB09994A1AF06684: C4311.1, R4349.2, R4350.1, U4343.3 (+)
XE63A0B74B293D479E1AC: U4324.11
XE96B3983355573610FBE: U4314.12, U4318.13, U4320.2, U4331.9 (Q), U4334.2 (D)
XE27181901B0CE18BFC8D: R4374.2, R4375.2, RV4306.2 (Wiper), RV4306.3 (CW), U4341.2 (-)
XEC42086D6EC8E9189C8B: D4305.3 (COM), R4356.2, U4343.12 (+)
XEF4ACAF335DFBA297C14: U4324.6, U4324.9
XEF04C3748B399D6D7D6A: U4323.2, U4336.5 (Q)
XEF4265C1B70D33EA5930: R4319.2, R4320.2, U4309.3 (+)
XF1A6DD158C1CD61C9877: U4325.6, U4325.9, U4325.10
XF4BD1DC9700368C0D180: R4353.1, R4354.1, U4343.7
XF4EC3AE7692D0F5EBBB4: U4323.11, U4338.2 (D)
XF15F90BA5572340B3BAF: R4359.2, RV4302.1 (CCW)
XF26A929B7CFAC028786A: R4302.1, R4358.1, R4375.1, RV4304.1 (CCW), RV4308.1 (CCW), U4339.7
XF29F6C5C6644D9B243DF: U4315.4, U4333.9 (Q)
XF4160D83D5951731749B: R4391.2, R4392.1, U4307.3 (+)
XF15225BE896AFDBBACB8: U4319.8, U4337.2 (D)
XF374688ABC00ED7D5F1F: R4319.1, U4339.8, U4339.9 (-)
XF507652F2B4294329012: R4359.1, R4360.1, U4340.8
XF50257526A2D450135BE: U4325.3, U4325.13
XFBCC481532BD505050A6: R4381.2, R4382.1, U4307.14 (+)
XFD9947C287C87406B2B4: R4354.2, R4355.2, U4343.9 (-)
XFD300825A6FE9E42E993: R4393.2, R4394.1, U4307.13 (-)
