Takazudo/zudo-osc-hole-field/boards/osc-core/sheets/envelope_E4_K.kicad_sch

## KiCad design boards/osc-core/sheets/envelope_E4_K.kicad_sch (2026-10-05)

Schematic: envelope_E4_K.kicad_sch

Parts:
C4401: 1e-07 F; C0603; MPN GRM188R71H104KA93D
C4402: 1e-06 F; C0603
C4408: 1 µF; C0603
C4409: 1 nF C0G; C0603
C4410, C4413: 100 nF C0G; C1206; MPN 1206CG104J500NT; LCSC C46348
C4411, C4412: 1e-08 F; C0603
C4414, C4421, C4422, C4423, C4424, C4425, C4426, C4427, C4428, C4429, C4430, C4431, C4432, C4433, C4434, C4435, C4436, C4437, C4438, C4439, C4440, C4441, C4442, C4443, C4444, C4445, C4446, C4447, C4448, C4449, C4450, C4451, C4452, C4453, C4454, C4455, C4457, C4458, C4459, C4460, C4461, C4462, C4463, C4466, C4467, C4468, C4469, C4470, C4471: 100 nF; C0603; MPN GRM188R71H104KA93D
D4404: BAS16GW-QX; SOD-123; MPN BAS16GW-QX
D4405, D4406: BAT54S,215; SOT-23; MPN BAT54S,215
Q4401, Q4404: BCM847BS,115; SOT-363_SC-70-6; MPN BCM847BS,115
Q4402, Q4403, Q4405, Q4406: MMBT3906,215; SOT-23; MPN MMBT3906,215
R4401, R4402, R4419: 10000 Ω; R0603
R4403: 22000 Ω; R0603
R4404, R4417: 100000 Ω; R0603; MPN RT0603BRD07100KL
R4418: 33200 Ω; R0603
R4420: 390000 Ω; R0603
R4421: 4700 Ω; R0603
R4432, R4436, R4438, R4443, R4445, R4451, R4453, R4454, R4455, R4457, R4468, R4470, R4471, R4472, R4474, R4483, R4484, R4485, R4486, R4487, R4488, R4489, R4490: 100 kΩ; R0603; MPN RT0603BRD07100KL
R4433, R4434: 47 kΩ; R0603
R4435: 60 kΩ; R0603
R4437: 80 kΩ; R0603
R4439: 40 kΩ; R0603
R4440, R4456, R4473: 10 kΩ; R0603
R4441: 79 kΩ; R0603
R4442, R4462, R4463, R4479, R4480: 22 kΩ; R0603
R4444, R4446: 10 MΩ; R0603
R4447, R4448: 4.7 kΩ; R0603
R4449, R4466: 1000 Ω; R0603
R4450, R4467: 1e+07 Ω; R0603
R4452, R4458, R4469, R4475: 200 kΩ; R0603
R4459, R4476: 3.3 kΩ; R0603
R4460, R4465, R4477, R4482, R4492, R4494: 1 kΩ; R0603
R4461, R4478: 300 kΩ; R0603
R4464, R4481: 470 kΩ; R0603
R4491, R4493: 899 kΩ; R0603
R4495, R4496, R4497, R4498: 100 Ω; R0603
R4499: 64 kΩ; R0603
RB4401: 80 kΩ; R0603
RB4402, RB4403: 100 kΩ; R0603; MPN RT0603BRD07100KL
RB4404: 400 kΩ; R0603
RV4402, RV4406: 1 kΩ; Potentiometer_Bourns_TC33X_Vertical; MPN TC33X-2-102E
RV4403, RV4407: 50 kΩ; Potentiometer_Bourns_TC33X_Vertical
RV4404, RV4408: 10 kΩ; Potentiometer_Bourns_TC33X_Vertical; MPN TC33X-2-103E
U4401: REF5050AIDR; SOIC-8_3.9x4.9mm_P1.27mm; MPN REF5050AIDR; LCSC C27804
U4405: CD74HC221M96; SOIC-16_3.9x9.9mm_P1.27mm; MPN CD74HC221M96; LCSC C133954
U4406, U4408: ADG5412FBRUZ; TSSOP-16_4.4x5mm_P0.65mm; MPN ADG5412FBRUZ; LCSC C579073
U4407: LM13700M/NOPB; SOIC-16_3.9x9.9mm_P1.27mm; MPN LM13700M/NOPB; LCSC C1346265
U4409, U4410: LM393BIDR; SOIC-8_3.9x4.9mm_P1.27mm; MPN LM393BIDR
U4412: SN74HC14DR; SOIC-14_3.9x8.7mm_P1.27mm; MPN SN74HC14DR
U4413, U4414, U4415, U4416, U4417, U4418, U4419, U4420, U4421, U4422, U4423, U4424, U4425, U4426, U4427, U4428, U4429: SN74HC00DR; SOIC-14_3.9x8.7mm_P1.27mm; MPN SN74HC00DR
U4430, U4431, U4432, U4433, U4434, U4435, U4436, U4437, U4438: SN74HC74DR; SOIC-14_3.9x8.7mm_P1.27mm; MPN SN74HC74DR
U4439, U4440, U4441: OPA4197IPWR; TSSOP-14_4.4x5mm_P0.65mm; MPN OPA4197IPWR; LCSC C2057327
U4443, U4444, U4445: OPA4196IDR; SOIC-14_3.9x8.7mm_P1.27mm; MPN OPA4196IDR; LCSC C2057385

Connections:
+5V: C4421.1, C4430.1, C4431.1, C4432.1, C4433.1, C4434.1, C4435.1, C4436.1, C4437.1, C4438.1, C4439.1, C4440.1, C4441.1, C4442.1, C4443.1, C4444.1, C4445.1, C4446.1, C4447.1, C4448.1, C4449.1, C4450.1, C4451.1, C4452.1, C4453.1, C4454.1, C4455.1, C4457.1, D4404.1 (K), R4421.1, R4432.1, R4434.1, R4447.1, R4448.1, U4405.16 (VCC), U4412.14 (VCC), U4413.14 (VCC), U4414.14 (VCC), U4415.14 (VCC), U4416.14 (VCC), U4417.14 (VCC), U4418.14 (VCC), U4419.14 (VCC), U4420.14 (VCC), U4421.14 (VCC), U4422.14 (VCC), U4423.14 (VCC), U4424.14 (VCC), U4425.14 (VCC), U4426.14 (VCC), U4427.14 (VCC), U4428.14 (VCC), U4429.14 (VCC), U4430.2 (D), U4430.4 (~S), U4430.10 (~S), U4430.14 (VCC), U4431.4 (~S), U4431.10 (~S), U4431.14 (VCC), U4432.4 (~S), U4432.10 (~S), U4432.14 (VCC), U4433.4 (~S), U4433.10 (~S), U4433.14 (VCC), U4434.4 (~S), U4434.10 (~S), U4434.14 (VCC), U4435.4 (~S), U4435.10 (~S), U4435.14 (VCC), U4436.4 (~S), U4436.10 (~S), U4436.14 (VCC), U4437.4 (~S), U4437.10 (~S), U4437.14 (VCC), U4438.4 (~S), U4438.10 (~S), U4438.14 (VCC)
+12V: C4401.1, C4414.1, C4422.1, C4424.1, C4426.1, C4428.1, C4429.1, C4458.1, C4460.1, C4462.1, C4466.1, C4468.1, C4470.1, Q4402.2 (E), Q4403.2 (E), Q4405.2 (E), Q4406.2 (E), U4401.2 (Vin), U4406.13 (VDD), U4407.11 (V+), U4408.13 (VDD), U4409.8 (V+), U4410.8 (V+), U4439.4 (V+), U4440.4 (V+), U4441.4 (V+), U4443.4 (V+), U4444.4 (V+), U4445.4 (V+)
-12V: C4423.1, C4425.1, C4427.1, C4459.1, C4461.1, C4463.1, C4467.1, C4469.1, C4471.1, U4406.4 (VSS), U4407.6 (V-), U4408.4 (VSS), U4439.11 (V-), U4440.11 (V-), U4441.11 (V-), U4443.11 (V-), U4444.11 (V-), U4445.11 (V-)
AGND: C4401.2, C4402.2, C4408.2, C4409.2, C4411.2, C4412.2, C4413.2, C4414.2, C4421.2, C4422.2, C4423.2, C4424.2, C4425.2, C4426.2, C4427.2, C4428.2, C4429.2, C4430.2, C4431.2, C4432.2, C4433.2, C4434.2, C4435.2, C4436.2, C4437.2, C4438.2, C4439.2, C4440.2, C4441.2, C4442.2, C4443.2, C4444.2, C4445.2, C4446.2, C4447.2, C4448.2, C4449.2, C4450.2, C4451.2, C4452.2, C4453.2, C4454.2, C4455.2, C4457.2, C4458.2, C4459.2, C4460.2, C4461.2, C4462.2, C4463.2, C4466.2, C4467.2, C4468.2, C4469.2, C4470.2, C4471.2, D4405.1 (A), D4406.1 (A), Q4401.2 (B1), Q4404.2 (B1), R4404.2, R4436.2, R4438.2, R4440.2, R4442.2, R4450.2, R4465.2, R4467.2, R4482.2, R4484.2, R4490.2, R4492.2, R4494.2, RB4401.2, RB4404.2, U4401.4 (GND), U4405.1 (1A), U4405.8 (GND), U4405.9 (2A), U4405.10 (2B), U4405.11 (2R), U4406.5 (GND), U4407.7, U4407.10, U4408.5 (GND), U4408.6 (S4), U4408.7 (D4), U4408.8 (IN4), U4408.9 (IN3), U4408.10 (D3), U4408.11 (S3), U4408.15 (D2), U4409.4 (GND), U4410.4 (GND), U4410.5 (+), U4412.7 (GND), U4413.7 (GND), U4414.7 (GND), U4415.7 (GND), U4416.7 (GND), U4417.7 (GND), U4418.7 (GND), U4419.7 (GND), U4420.7 (GND), U4421.7 (GND), U4422.7 (GND), U4423.7 (GND), U4424.7 (GND), U4425.7 (GND), U4426.7 (GND), U4427.7 (GND), U4428.7 (GND), U4429.7 (GND), U4429.12, U4429.13, U4430.7 (GND), U4431.7 (GND), U4432.7 (GND), U4433.7 (GND), U4434.7 (GND), U4435.7 (GND), U4436.7 (GND), U4437.7 (GND), U4438.7 (GND), U4438.11 (C), U4438.12 (D), U4438.13 (~R), U4439.5 (+), U4440.10 (+), U4440.12 (+), U4441.3 (+), U4441.5 (+), U4441.12 (+), U4443.5 (+), U4443.10 (+), U4444.5 (+), U4444.10 (+), U4445.12 (+)
X0C6D5F78E32943DCB854: U4422.11, U4423.1, U4428.4, U4428.12
X0D23E7FB1DB8342F88D2: U4416.4, U4418.5, U4420.1, U4432.9 (Q)
X0E99891B917C9A02F224: R4459.1, R4460.1, U4440.8
X0F5AFD4ACC632F96D55E: U4419.11, U4421.4
X1AE7223F58A3B55D52B4: U4423.11, U4438.2 (D)
X1D2905710F7095314259: R4464.1, RV4404.2 (Wiper)
X1E8CB1D7E95F78F1A6C3: R4444.1, R4447.2, U4409.7, U4412.11
X1E38D29F237472EBDA26: C4409.1, R4433.2, U4412.9
X1ED8F13C07BED63C2F05: R4489.2, R4490.1, U4445.6 (-)
X2A707E8D87F5DA2B2220: U4441.13 (-), U4441.14
X2D8D21FDD630C3EA32C6: U4428.6, U4428.9, U4428.10
X2D12E8800AF4537DED79: R4486.1, U4406.15 (D2), U4445.1
X3B0683EE68B560E71165: U4423.6, U4423.9
X3CAFA431F9E467FA3BC2: R4459.2, RV4402.1 (CCW)
X4A4AC40D3DE6805BF277: U4423.2, U4436.5 (Q)
X4A4ED37F3A32AB4D1D34: U4421.3, U4421.13
X4A5F0B998AD85F74FC61: R4493.1, U4406.6 (S4), U4406.11 (S3)
X4BAD2FD40711D34828FA: Q4406.3 (C), R4480.1
X4C2D151CEDB74B0A7CF9: U4422.6, U4437.12 (D)
X4DC1C190A7E65B406B86: U4405.3 (1R), U4422.9, U4425.4, U4426.12, U4430.9 (Q), U4431.1 (~R), U4431.13 (~R), U4432.1 (~R), U4432.13 (~R), U4433.1 (~R), U4433.13 (~R), U4434.1 (~R), U4434.13 (~R), U4435.1 (~R), U4435.13 (~R), U4436.1 (~R), U4436.13 (~R), U4437.1 (~R), U4437.13 (~R), U4438.1 (~R)
X4EC939E51704CEA8DC0A: U4413.8, U4431.2 (D)
X4ED0DFA94DEFD4FDA1F9: U4416.10, U4435.6 (~Q)
X5A6FDAA43634D6E8FD5C: U4414.8, U4415.5
X5ACAD559F2D38BFEF83D: U4418.11, U4419.1, U4419.2
X5B93FCF8EC2861D3B6DB: U4435.9 (Q), U4436.2 (D)
X5FD3ED65BA431112FEE6: U4412.10, U4426.2, U4434.12 (D)
X6A8EF71CF9A6057D4F93: U4413.6, U4413.10
X6C5B25BE6EEE7C1A0696: U4419.8, U4437.2 (D)
X7AFCA596192D5DEB6126: U4416.5, U4431.8 (~Q)
X7C1C4BF507F3B1BC5CA4: U4415.3, U4415.13
X7D78D8C31A2973EBBCD1: R4451.1, U4443.1, U4443.2 (-)
X7E8D6473E903D0D81319: U4412.6, U4430.1 (~R), U4430.13 (~R)
X8C1267C018CC29663DB0: U4425.8, U4425.12
X9AAAB210197FC422D1E7: U4421.1, U4437.5 (Q)
X9B532A7E781E03EF166D: R4445.1, R4489.1, U4406.7 (D4), U4409.6 (-), U4445.7
X9B81034A8BEE6B2EBDA4: U4429.6
X9D0164D30AA9FEDC29E9: R4491.1, U4406.2 (D1), U4406.14 (S2)
X9D53207805B8DB8B6983: U4405.4 (1Q), U4415.1, U4415.2
X9DFC7E54D7F34EDCEBA8: U4414.3, U4414.4
X10FE9831716BD55F6884: U4417.6, U4417.9, U4418.4, U4422.1, U4423.10
X11FD029782B329BAC0F5: U4433.2 (D)
X15D562376CCAACF39837: U4422.8, U4422.12, U4422.13
X18DF7051EF7F8303A783: U4418.3, U4419.5
X028F66162D3B15CD6E92: U4413.11, U4414.1, U4414.2
X37A2B9BDC0CB91FADA08: Q4404.3 (C2), R4479.2
X37DB23C939E6F7760724: U4427.11, U4428.1, U4428.2
X39E257BD9EEFCA651BEE: C4410.1, R4434.2, U4405.15 (1RXCX)
X42E898BF29DB21014DB5: R4437.1, R4443.1, R4483.1, U4406.3 (S1), U4406.10 (D3), U4440.1
X43F96F7BEB8A4E4C6C53: R4476.1, R4477.1, U4441.1
X48EF72FBEE4E2C2D161F: U4415.4, U4433.9 (Q)
X53DB4FD2AA437D16728B: U4420.8, U4420.13
X56A3DD88EAAF342C9925: U4427.3, U4427.4, U4427.12
X59FE89738C49A44651DE: U4423.3, U4423.4, U4423.5
X67DA6E837DC5E8E2ADE0: R4435.1, U4408.3 (S1), U4439.14
X68B3985989FCF7E28B74: U4422.3, U4422.4, U4422.5
X72DBC31D9719BB5A59BF: R4498.1, U4408.14 (S2)
X76BA09BBD8D074E4BB50: R4437.2, R4438.1, U4440.2 (-)
X79E6DE1D4CA995195D79: R4419.1, U4439.8, U4439.9 (-)
X82B0F2210FC0C330AC37: R4403.2, R4404.1, U4439.10 (+)
X84CA5ED9A4BDBE561C82: R4439.2, R4440.1, U4440.5 (+)
X88D1A44E36A22B77BEFF: R4469.1
X89A58516363F6FD3C600: R4463.2, U4407.1
X89D5E3CA45DE92E8F54F: D4405.2 (K), D4406.2 (K), R4401.1, R4403.1, R4418.1, R4439.1, R4441.1, R4461.1, R4478.1, RB4402.1, RV4404.3 (CW), RV4408.3 (CW), U4410.6 (-), U4439.1, U4439.2 (-), U4439.12 (+), U4440.3 (+)
X92ECCAF6453873873CA8: R4446.1, R4448.2, U4410.1, U4412.13
X95E38523BB35DF833AE9: R4485.1, R4487.1, R4499.1, U4441.8, U4441.9 (-)
X96EE559E54D2E0F972B1: U4415.8, U4415.12
X96F203C6F898BCDE98AB: U4425.6, U4425.9, U4425.10
X131A163062BE66F69054: U4429.8
X155E093570452C93A7DF: R4472.1, R4473.1, U4444.8
X212F0A9A822E636F424B: U4431.5 (Q), U4431.12 (D)
X253D95E3ACB7B4702D8D: R4441.2, R4442.1, U4410.2 (-)
X286DDDC3E2B74B97DC94: Q4401.6 (C1), RV4403.2 (Wiper), RV4403.3 (CW), U4440.13 (-)
X299CA8591EBFA4F5B786: U4430.5 (Q), U4430.12 (D)
X336AA44E374F457FBA82: R4420.1, R4421.2, U4409.1, U4412.1
X523A154D6CD32BA24CA2: R4468.2, R4469.2, R4470.2, U4444.6 (-)
X524EDD383A663D1C8FBE: U4417.3, U4417.10
X582B1994AE84F69245AC: Q4404.5 (B2), R4477.2
X593C3CC67277F2D2C14A: Q4404.1 (E1), Q4404.4 (E2), U4441.7
X608A124D8F6FFC40228B: U4406.1 (IN1), U4427.8
X760F91FF2473595B0A45: U4415.11, U4416.2
X776E4C872C6CACFB6981: U4419.13, U4436.6 (~Q)
X850C0774FC18D4F3AA9D: U4417.8, U4436.12 (D)
X862B85B7365A480D1EC4: RB4403.1, U4445.8
X0887C13EA610B06EDF19: R4487.2, R4488.2, U4445.5 (+)
X942D53601EE3F6C2124F: U4406.16 (IN2), U4428.3
X1035D09FE23AE8243DEA: U4412.2, U4413.1, U4413.2
X2495EC2B4A4A99BF1DA1: R4443.2, R4444.2, U4409.5 (+)
X3999A91FF8133B4A3AC1: U4414.5, U4437.8 (~Q)
X4149FC4412531C8DC406: U4420.6, U4420.9
X6019D7D0439E077F0FDD: R4445.2, R4446.2, U4410.3 (+)
X6290C60E986B1E4DB8AF: C4410.2, U4405.14 (1CX)
X7018A15E8CEBE354E48B: U4414.12, U4418.13, U4420.2, U4431.9 (Q), U4434.2 (D)
X7326DCB1EAF55CC4B716: C4411.1, R4449.2, R4450.1, U4443.3 (+)
X07470EB0E0E11C659D1B: U4428.11, U4429.1, U4429.2
X12526D06AC7BB87D9196: R4449.1
X12779E488E24F1864CD0: R4452.1
X36460D267067B3C8F5FF: C4412.1, R4466.2, R4467.1, U4444.3 (+)
X57995E21F32A6486EA34: R4454.2, R4455.2, U4443.9 (-)
X071784AA769D6ADB6967: U4417.11, U4418.2
X73897B2AC6B5D3876ECF: R4474.1, U4444.13 (-), U4444.14
X81607C5F0EEEB44F961C: R4491.2, R4492.1, U4407.3 (+)
X94393B171775D5651835: U4419.3, U4419.4
X196262AD72D337EE9FBF: R4470.1, R4471.1, U4444.7
X264345FD99DAE3BBB0F2: Q4403.3 (C), R4463.1
X0711264EB6D8A69B336B: U4424.8, U4424.13
X962315B86A524CCD203D: U4416.3, U4417.4, U4417.5
X3798166D7F8F13BD64A6: U4425.3, U4425.13
X5136206AF1CAE7CB80A3: Q4405.1 (B), Q4405.3 (C), Q4406.1 (B), R4479.1
X5564801AC56AB4FEB68E: U4420.11, U4421.5
X79542661D202D997CD26: U4412.4, U4412.5
X9355403049E26B49885E: R4471.2, R4472.2, U4444.9 (-)
X14489165961EB95B7CC4: U4432.2 (D)
XA3B5B83A947B2920BCAC: R4419.2, R4420.2, U4409.3 (+)
XA3B469CC521A063D88D9: U4408.1 (IN1), U4426.6
XA6BB919FF34A83D76EE5: U4414.11, U4416.1
XA7EA78821ED6EC755972: R4474.2, R4475.2, RV4406.2 (Wiper), RV4406.3 (CW), U4441.2 (-)
XA9CD6E60F57615AD117A: R4435.2, R4436.1, U4439.13 (-)
XA63D3F861FFE1D109DF3: U4426.3, U4426.5
XA485A04AF81D21F345C4: R4417.1
XA2552F8335283172EE06: U4427.6, U4427.9, U4427.10
XA6247FCD3E46353970D3: U4416.8, U4416.12, U4416.13
XA77393E98C30C0F4BCC1: R4485.2, R4486.2, U4445.2 (-)
XAABE3B2B73AE6287C63B: R4466.1
XAD22CAA5ED18C77AC6C6: U4421.6, U4421.9, U4421.10
XADB8995F2A41812921CE: U4417.13, U4420.4, U4435.5 (Q)
XB0BE9D45FBD1D0ABB573: D4406.3 (COM), R4473.2, U4444.12 (+)
XB2C21643C876FF8DDF4F: U4445.13 (-), U4445.14
XB2F3DB94BF7BF9B0FAA0: U4413.4, U4413.5
XB3C46A3514BE888188AF: U4408.16 (IN2), U4425.11
XB4FA2626CB4D97D94057: C4402.1, U4401.6 (Vout), U4439.3 (+)
XB7D58D3F19F2EB99F9D9: R4496.1, U4407.12
XB014AFFA91A7D810360A: U4424.3, U4424.12
XB35A8DAC7E41BA150C74: Q4401.3 (C2), R4462.2
XB88F9AB4DE597C6A1EBE: U4426.8, U4427.5, U4428.5
XB876D2CA047353834170: R4495.1, U4407.5
XB1755A15F87901219DD1: U4424.11
XB843204A97311BEB6B07: Q4401.1 (E1), Q4401.4 (E2), U4440.14
XB31477966BAAD3C40431: U4416.11, U4417.1
XB93014181E2AAEAF45A4: R4468.1, U4444.1, U4444.2 (-)
XBB8DF6359A842D9F9FA7: R4457.1, U4443.13 (-), U4443.14
XBE9AFAD39D036B48CB2B: U4406.9 (IN3), U4428.8
XC1F9105B81D3F7050C05: R4433.1, U4412.8, U4430.3 (C), U4430.11 (C), U4431.3 (C), U4431.11 (C), U4432.3 (C), U4432.11 (C), U4433.3 (C), U4433.11 (C), U4434.3 (C), U4434.11 (C), U4435.3 (C), U4435.11 (C), U4436.3 (C), U4436.11 (C), U4437.3 (C), U4437.11 (C), U4438.3 (C)
XC6FACB0F3F210856521E: R4402.1, R4458.1, R4475.1, RV4404.1 (CCW), RV4408.1 (CCW), U4439.7
XC61FCAFDA16854045D13: U4420.3, U4420.5, U4421.2
XC6873A5301596BB2CEDC: C4413.1, R4495.2, R4496.2, R4497.2, R4498.2, U4441.10 (+)
XC8522B0B99E2B795ACEB: R4493.2, R4494.1, U4407.13 (-)
XC49435EB3A84C44DBCBE: U4412.12, U4425.2, U4435.12 (D)
XC8635494FD98C4F7D6C4: R4480.2, U4407.16
XCA6AB0EE57F37BA09AD7: R4451.2, R4452.2, R4453.2, U4443.6 (-)
XCB41D34D13C2DEF6A349: D4405.3 (COM), R4456.2, U4443.12 (+)
XCBC68FCBBC6BFD5235BE: R4401.2, R4402.2, U4439.6 (-)
XCD327D7864F888F85B84: U4423.8, U4423.12, U4423.13
XCE6BC31263AA083C91E8: U4426.9, U4426.10, U4427.13, U4428.13
XCEE55A37C6E228277850: R4457.2, R4458.2, RV4402.2 (Wiper), RV4402.3 (CW), U4440.9 (-)
XD7D6D91E0E862F9F43E5: Q4401.5 (B2), R4460.2
XD70E3955A8F68C958B03: U4416.6, U4417.2, U4420.10
XD71CDB30D2253E0A7794: R4481.2, R4482.1, U4407.14 (+)
XD569AE1B4503E80B3D7F: U4426.11, U4427.1, U4427.2
XD9263F5304825CF8D67D: U4434.9 (Q), U4435.2 (D)
XD46401791D744CEEBDD1: U4421.11, U4422.2
XD54485287726D0955171: U4419.6, U4419.9, U4419.10
XDA2D33611061D2224862: U4413.12, U4436.8 (~Q)
XDAD567798DDA5F8396F8: C4408.1, D4404.2 (A), R4432.2, U4412.3
XDC71D774AC2E1E560A2D: U4413.3, U4413.9
XDCC3F61322049840F5F3: U4413.13, U4418.1, U4426.4, U4437.6 (~Q)
XDCFDFC3A9673B361F0B6: U4419.12, U4422.10, U4424.2, U4425.1, U4429.9, U4429.10, U4437.9 (Q)
XDE2C523C3EBBA2A16600: R4417.2, R4418.2, U4409.2 (-)
XDE9A754283FDD78CEC08: Q4402.1 (B), Q4402.3 (C), Q4403.1 (B), R4462.1
XE02F5347A1FE54177E3F: R4497.1, U4408.2 (D1)
XE5B33D3D418CB150BF3D: U4414.13, U4434.6 (~Q)
XE66BC541D778AE1334AB: R4464.2, R4465.1, U4407.4 (-)
XE219DA8CFAB78541F232: R4478.2, RV4407.1 (CCW)
XE966D9E59F27CF55B0D0: U4415.6, U4415.9, U4415.10
XEAB0A8F9BE52E35B2801: Q4404.6 (C1), RV4407.2 (Wiper), RV4407.3 (CW), U4441.6 (-)
XEBD7B613ECE297C53D64: U4424.6, U4424.9
XEDF3BA73B67A9DE18027: U4418.8, U4418.12
XEFF9DAB4A101604FE8B8: U4418.6, U4418.9, U4418.10
XF4AD1470EFE7D63A46E7: R4453.1, R4454.1, U4443.7
XF4CA5DCFDABC750B445E: R4476.2, RV4406.1 (CCW)
XF5F945E041AE420297D7: U4424.1, U4424.4, U4424.5
XF6E38A8AD2CA4AFFFF0E: R4499.2, RB4401.1, U4445.10 (+)
XF6FD63623A71C0E3EAC1: R4481.1, RV4408.2 (Wiper)
XF27A2B641E24DFC7AF45: R4483.2, R4484.1, U4445.3 (+)
XF52EB94D4DB13A85C359: U4432.5 (Q), U4432.12 (D)
XF661DB3B62A41D6046D4: U4421.8, U4421.12
XF0947B9CA7FE448E4DE7: U4416.9, U4417.12, U4420.12, U4424.10, U4426.1, U4426.13, U4429.4, U4429.5, U4436.9 (Q)
XF59806A843ECC8E86334: U4414.6, U4414.9, U4414.10, U4425.5
XF927317D96C0673620FB: R4488.1, U4440.6 (-), U4440.7
XF4096975080530F2AF6E: R4455.1, R4456.1, U4443.8
XFE6A2349C3A8A70DC020: RB4402.2, RB4403.2, RB4404.1, U4445.9 (-)
XFE696A632A8F40C27552: U4433.5 (Q), U4433.12 (D)
XFF8AA17C0E1F34B14271: R4461.2, RV4403.1 (CCW)
XFF94BB01F01FB49E6872: U4405.2 (1B), U4438.5 (Q)
XFFD03A2F672514B13FBA: U4406.8 (IN4), U4429.3
