Takazudo/zudo-osc-hole-field/boards/osc-core/sheets/envelope_E5_K.kicad_sch

## KiCad design boards/osc-core/sheets/envelope_E5_K.kicad_sch (2026-10-05)

Schematic: envelope_E5_K.kicad_sch

Parts:
C4501: 1e-07 F; C0603; MPN GRM188R71H104KA93D
C4502: 1e-06 F; C0603
C4508: 1 µF; C0603
C4509: 1 nF C0G; C0603
C4510, C4513: 100 nF C0G; C1206; MPN 1206CG104J500NT; LCSC C46348
C4511, C4512: 1e-08 F; C0603
C4514, C4521, C4522, C4523, C4524, C4525, C4526, C4527, C4528, C4529, C4530, C4531, C4532, C4533, C4534, C4535, C4536, C4537, C4538, C4539, C4540, C4541, C4542, C4543, C4544, C4545, C4546, C4547, C4548, C4549, C4550, C4551, C4552, C4553, C4554, C4555, C4557, C4558, C4559, C4560, C4561, C4562, C4563, C4566, C4567, C4568, C4569, C4570, C4571: 100 nF; C0603; MPN GRM188R71H104KA93D
D4504: BAS16GW-QX; SOD-123; MPN BAS16GW-QX
D4505, D4506: BAT54S,215; SOT-23; MPN BAT54S,215
Q4501, Q4504: BCM847BS,115; SOT-363_SC-70-6; MPN BCM847BS,115
Q4502, Q4503, Q4505, Q4506: MMBT3906,215; SOT-23; MPN MMBT3906,215
R4501, R4502, R4519: 10000 Ω; R0603
R4503: 22000 Ω; R0603
R4504, R4517: 100000 Ω; R0603; MPN RT0603BRD07100KL
R4518: 33200 Ω; R0603
R4520: 390000 Ω; R0603
R4521: 4700 Ω; R0603
R4532, R4536, R4538, R4543, R4545, R4551, R4553, R4554, R4555, R4557, R4568, R4570, R4571, R4572, R4574, R4583, R4584, R4585, R4586, R4587, R4588, R4589, R4590: 100 kΩ; R0603; MPN RT0603BRD07100KL
R4533, R4534: 47 kΩ; R0603
R4535: 60 kΩ; R0603
R4537: 80 kΩ; R0603
R4539: 40 kΩ; R0603
R4540, R4556, R4573: 10 kΩ; R0603
R4541: 79 kΩ; R0603
R4542, R4562, R4563, R4579, R4580: 22 kΩ; R0603
R4544, R4546: 10 MΩ; R0603
R4547, R4548: 4.7 kΩ; R0603
R4549, R4566: 1000 Ω; R0603
R4550, R4567: 1e+07 Ω; R0603
R4552, R4558, R4569, R4575: 200 kΩ; R0603
R4559, R4576: 3.3 kΩ; R0603
R4560, R4565, R4577, R4582, R4592, R4594: 1 kΩ; R0603
R4561, R4578: 300 kΩ; R0603
R4564, R4581: 470 kΩ; R0603
R4591, R4593: 899 kΩ; R0603
R4595, R4596, R4597, R4598: 100 Ω; R0603
R4599: 64 kΩ; R0603
RB4501: 80 kΩ; R0603
RB4502, RB4503: 100 kΩ; R0603; MPN RT0603BRD07100KL
RB4504: 400 kΩ; R0603
RV4502, RV4506: 1 kΩ; Potentiometer_Bourns_TC33X_Vertical; MPN TC33X-2-102E
RV4503, RV4507: 50 kΩ; Potentiometer_Bourns_TC33X_Vertical
RV4504, RV4508: 10 kΩ; Potentiometer_Bourns_TC33X_Vertical; MPN TC33X-2-103E
U4501: REF5050AIDR; SOIC-8_3.9x4.9mm_P1.27mm; MPN REF5050AIDR; LCSC C27804
U4505: CD74HC221M96; SOIC-16_3.9x9.9mm_P1.27mm; MPN CD74HC221M96; LCSC C133954
U4506, U4508: ADG5412FBRUZ; TSSOP-16_4.4x5mm_P0.65mm; MPN ADG5412FBRUZ; LCSC C579073
U4507: LM13700M/NOPB; SOIC-16_3.9x9.9mm_P1.27mm; MPN LM13700M/NOPB; LCSC C1346265
U4509, U4510: LM393BIDR; SOIC-8_3.9x4.9mm_P1.27mm; MPN LM393BIDR
U4512: SN74HC14DR; SOIC-14_3.9x8.7mm_P1.27mm; MPN SN74HC14DR
U4513, U4514, U4515, U4516, U4517, U4518, U4519, U4520, U4521, U4522, U4523, U4524, U4525, U4526, U4527, U4528, U4529: SN74HC00DR; SOIC-14_3.9x8.7mm_P1.27mm; MPN SN74HC00DR
U4530, U4531, U4532, U4533, U4534, U4535, U4536, U4537, U4538: SN74HC74DR; SOIC-14_3.9x8.7mm_P1.27mm; MPN SN74HC74DR
U4539, U4540, U4541: OPA4197IPWR; TSSOP-14_4.4x5mm_P0.65mm; MPN OPA4197IPWR; LCSC C2057327
U4543, U4544, U4545: OPA4196IDR; SOIC-14_3.9x8.7mm_P1.27mm; MPN OPA4196IDR; LCSC C2057385

Connections:
+5V: C4521.1, C4530.1, C4531.1, C4532.1, C4533.1, C4534.1, C4535.1, C4536.1, C4537.1, C4538.1, C4539.1, C4540.1, C4541.1, C4542.1, C4543.1, C4544.1, C4545.1, C4546.1, C4547.1, C4548.1, C4549.1, C4550.1, C4551.1, C4552.1, C4553.1, C4554.1, C4555.1, C4557.1, D4504.1 (K), R4521.1, R4532.1, R4534.1, R4547.1, R4548.1, U4505.16 (VCC), U4512.14 (VCC), U4513.14 (VCC), U4514.14 (VCC), U4515.14 (VCC), U4516.14 (VCC), U4517.14 (VCC), U4518.14 (VCC), U4519.14 (VCC), U4520.14 (VCC), U4521.14 (VCC), U4522.14 (VCC), U4523.14 (VCC), U4524.14 (VCC), U4525.14 (VCC), U4526.14 (VCC), U4527.14 (VCC), U4528.14 (VCC), U4529.14 (VCC), U4530.2 (D), U4530.4 (~S), U4530.10 (~S), U4530.14 (VCC), U4531.4 (~S), U4531.10 (~S), U4531.14 (VCC), U4532.4 (~S), U4532.10 (~S), U4532.14 (VCC), U4533.4 (~S), U4533.10 (~S), U4533.14 (VCC), U4534.4 (~S), U4534.10 (~S), U4534.14 (VCC), U4535.4 (~S), U4535.10 (~S), U4535.14 (VCC), U4536.4 (~S), U4536.10 (~S), U4536.14 (VCC), U4537.4 (~S), U4537.10 (~S), U4537.14 (VCC), U4538.4 (~S), U4538.10 (~S), U4538.14 (VCC)
+12V: C4501.1, C4514.1, C4522.1, C4524.1, C4526.1, C4528.1, C4529.1, C4558.1, C4560.1, C4562.1, C4566.1, C4568.1, C4570.1, Q4502.2 (E), Q4503.2 (E), Q4505.2 (E), Q4506.2 (E), U4501.2 (Vin), U4506.13 (VDD), U4507.11 (V+), U4508.13 (VDD), U4509.8 (V+), U4510.8 (V+), U4539.4 (V+), U4540.4 (V+), U4541.4 (V+), U4543.4 (V+), U4544.4 (V+), U4545.4 (V+)
-12V: C4523.1, C4525.1, C4527.1, C4559.1, C4561.1, C4563.1, C4567.1, C4569.1, C4571.1, U4506.4 (VSS), U4507.6 (V-), U4508.4 (VSS), U4539.11 (V-), U4540.11 (V-), U4541.11 (V-), U4543.11 (V-), U4544.11 (V-), U4545.11 (V-)
AGND: C4501.2, C4502.2, C4508.2, C4509.2, C4511.2, C4512.2, C4513.2, C4514.2, C4521.2, C4522.2, C4523.2, C4524.2, C4525.2, C4526.2, C4527.2, C4528.2, C4529.2, C4530.2, C4531.2, C4532.2, C4533.2, C4534.2, C4535.2, C4536.2, C4537.2, C4538.2, C4539.2, C4540.2, C4541.2, C4542.2, C4543.2, C4544.2, C4545.2, C4546.2, C4547.2, C4548.2, C4549.2, C4550.2, C4551.2, C4552.2, C4553.2, C4554.2, C4555.2, C4557.2, C4558.2, C4559.2, C4560.2, C4561.2, C4562.2, C4563.2, C4566.2, C4567.2, C4568.2, C4569.2, C4570.2, C4571.2, D4505.1 (A), D4506.1 (A), Q4501.2 (B1), Q4504.2 (B1), R4504.2, R4536.2, R4538.2, R4540.2, R4542.2, R4550.2, R4565.2, R4567.2, R4582.2, R4584.2, R4590.2, R4592.2, R4594.2, RB4501.2, RB4504.2, U4501.4 (GND), U4505.1 (1A), U4505.8 (GND), U4505.9 (2A), U4505.10 (2B), U4505.11 (2R), U4506.5 (GND), U4507.7, U4507.10, U4508.5 (GND), U4508.6 (S4), U4508.7 (D4), U4508.8 (IN4), U4508.9 (IN3), U4508.10 (D3), U4508.11 (S3), U4508.15 (D2), U4509.4 (GND), U4510.4 (GND), U4510.5 (+), U4512.7 (GND), U4513.7 (GND), U4514.7 (GND), U4515.7 (GND), U4516.7 (GND), U4517.7 (GND), U4518.7 (GND), U4519.7 (GND), U4520.7 (GND), U4521.7 (GND), U4522.7 (GND), U4523.7 (GND), U4524.7 (GND), U4525.7 (GND), U4526.7 (GND), U4527.7 (GND), U4528.7 (GND), U4529.7 (GND), U4529.12, U4529.13, U4530.7 (GND), U4531.7 (GND), U4532.7 (GND), U4533.7 (GND), U4534.7 (GND), U4535.7 (GND), U4536.7 (GND), U4537.7 (GND), U4538.7 (GND), U4538.11 (C), U4538.12 (D), U4538.13 (~R), U4539.5 (+), U4540.10 (+), U4540.12 (+), U4541.3 (+), U4541.5 (+), U4541.12 (+), U4543.5 (+), U4543.10 (+), U4544.5 (+), U4544.10 (+), U4545.12 (+)
X0AE84336D8D2152397FC: Q4504.3 (C2), R4579.2
X0C0E378638CF29645AC0: R4519.1, U4539.8, U4539.9 (-)
X00F1AF4E1A8932F6B746: U4521.8, U4521.12
X1CBC71D32BE5EF97462C: U4525.6, U4525.9, U4525.10
X1CF00E175CAFC2A0EC1A: U4522.3, U4522.4, U4522.5
X1E5E726E8BFBF2C8D7CB: R4566.1
X1FF37C40C508F047CAB6: U4514.8, U4515.5
X02CB8FF55279DAA45A09: U4532.2 (D)
X2D3D0B83E69B8C6F6A0E: U4506.1 (IN1), U4527.8
X2D621D3FA174AA2A0488: R4589.2, R4590.1, U4545.6 (-)
X2E94D5286A01140BA891: R4597.1, U4508.2 (D1)
X2E118744DA9E50F80954: U4515.6, U4515.9, U4515.10
X2F1EA6364C8758A2E876: U4519.3, U4519.4
X3A851D34D417A44F2193: U4520.8, U4520.13
X3C8CF8719E4CDD85EBBC: U4514.12, U4518.13, U4520.2, U4531.9 (Q), U4534.2 (D)
X3CB093BB7419E86B97DC: R4549.1
X3F3C53CC94BD95AE5C54: R4569.1
X03F6AD7066A869B8A620: R4568.2, R4569.2, R4570.2, U4544.6 (-)
X4BAC10B69130181AD1C5: U4517.13, U4520.4, U4535.5 (Q)
X4C566AE921CA694B6DB3: U4517.8, U4536.12 (D)
X4D2D4B889380FBB3BFF9: U4506.9 (IN3), U4528.8
X004DFD90139031AA481C: U4520.6, U4520.9
X4FDA5049D58C14E5BB5C: R4578.2, RV4507.1 (CCW)
X5A604CFE521FCCF99BB8: U4506.8 (IN4), U4529.3
X5D13DC7FEBD1DA25D131: R4539.2, R4540.1, U4540.5 (+)
X6ACC8608A6CCE61E473D: R4574.2, R4575.2, RV4506.2 (Wiper), RV4506.3 (CW), U4541.2 (-)
X6C46B9F7EBBF296B6591: U4508.16 (IN2), U4525.11
X6CAB6C6582E2AD649563: R4570.1, R4571.1, U4544.7
X7A5D564973EFC4B635A8: D4505.3 (COM), R4556.2, U4543.12 (+)
X7A60CDBDD22898ADD05B: U4505.4 (1Q), U4515.1, U4515.2
X7A2084E6C1D0FFEF33AC: U4514.6, U4514.9, U4514.10, U4525.5
X7CDA84E1439B64E89AD5: U4519.8, U4537.2 (D)
X7D94471AB32FDFA91B5F: Q4504.5 (B2), R4577.2
X7EF75494A4A77BA218D5: U4535.9 (Q), U4536.2 (D)
X8CC5C43B41A8FF14CD25: U4523.2, U4536.5 (Q)
X08D622B0DD6B0120E046: U4518.6, U4518.9, U4518.10
X8EBFCD512EA801330A10: R4563.2, U4507.1
X9BB5B2C73888398C9B12: R4568.1, U4544.1, U4544.2 (-)
X9CA7BE412266A2A54AFB: U4525.3, U4525.13
X9D2EDD8DEE2E50A411BE: U4519.11, U4521.4
X9DDFDC1A1851BFC7A703: R4543.2, R4544.2, U4509.5 (+)
X9E156B52437DD9D7B511: U4513.12, U4536.8 (~Q)
X10ECE023ED91D431A713: R4591.1, U4506.2 (D1), U4506.14 (S2)
X12B13EB7F3D1319D03B9: R4503.2, R4504.1, U4539.10 (+)
X15C7A15C86F90C636F3C: C4510.2, U4505.14 (1CX)
X15F35935EE308294E30D: R4559.2, RV4502.1 (CCW)
X23E52057CBCE7DB1EF65: U4526.3, U4526.5
X26D0D03F51E9F2BD8610: R4587.2, R4588.2, U4545.5 (+)
X32C8BF825499CC73BD2B: U4541.13 (-), U4541.14
X33E0E5D3CCBC6AE7FA75: U4516.11, U4517.1
X39F4FA9DE5DF024E24B1: R4517.2, R4518.2, U4509.2 (-)
X43CA65FE028A7BC0888C: U4528.6, U4528.9, U4528.10
X44C3263A0F15EFC08049: R4576.2, RV4506.1 (CCW)
X47D608DDF71348C73577: U4525.8, U4525.12
X54D2752F75F45F7F1124: U4516.5, U4531.8 (~Q)
X56E9892BA39034792866: U4518.11, U4519.1, U4519.2
X58ACEEEBFFEAC9A3F7F2: U4514.3, U4514.4
X58DAAE57A642301523BF: U4531.5 (Q), U4531.12 (D)
X65FCAD4B32001678EB38: U4514.11, U4516.1
X66B3992E4CA51A02FBEF: R4583.2, R4584.1, U4545.3 (+)
X68BB46DFE0780E2D1388: U4518.8, U4518.12
X69EBF5E259E534C822FC: R4588.1, U4540.6 (-), U4540.7
X71B9E05195347FA9C8C2: R4585.1, R4587.1, R4599.1, U4541.8, U4541.9 (-)
X72EA8955D5926ED47883: R4561.2, RV4503.1 (CCW)
X74FE612A599C88EF9232: U4513.4, U4513.5
X82BDD3A8784568B7E0A1: R4501.2, R4502.2, U4539.6 (-)
X83AE2E88790028F87CE8: R4572.1, R4573.1, U4544.8
X86E5FBAC783E74D0E0AF: U4517.3, U4517.10
X88CE732345F5CAF0A795: U4516.3, U4517.4, U4517.5
X152BA91D292A3C8E10FF: U4515.4, U4533.9 (Q)
X175BBF2534F2DB38978E: C4509.1, R4533.2, U4512.9
X179B20A4D231C26D551D: U4505.3 (1R), U4522.9, U4525.4, U4526.12, U4530.9 (Q), U4531.1 (~R), U4531.13 (~R), U4532.1 (~R), U4532.13 (~R), U4533.1 (~R), U4533.13 (~R), U4534.1 (~R), U4534.13 (~R), U4535.1 (~R), U4535.13 (~R), U4536.1 (~R), U4536.13 (~R), U4537.1 (~R), U4537.13 (~R), U4538.1 (~R)
X198B2BFD4E84A318BEFB: U4522.11, U4523.1, U4528.4, U4528.12
X241D8448B5CD7834CD3D: U4508.1 (IN1), U4526.6
X301A337AD7BD8225D55F: U4512.10, U4526.2, U4534.12 (D)
X341AF81BFE4FC2D3B202: R4591.2, R4592.1, U4507.3 (+)
X346DD33A417B8C52D3FF: RB4503.1, U4545.8
X471A731E845795DFDAD5: U4523.11, U4538.2 (D)
X502E89619C40AC1AA583: C4510.1, R4534.2, U4505.15 (1RXCX)
X524EE2BE38ADCEEC7AE7: U4522.8, U4522.12, U4522.13
X612DD40841C5836BEEE5: U4534.9 (Q), U4535.2 (D)
X696EB289B624B9E1FABE: U4519.6, U4519.9, U4519.10
X809C2C77FF65F9E5F32A: U4524.6, U4524.9
X856F998094D94C6332D7: R4564.1, RV4504.2 (Wiper)
X875D9160981F9817E4C8: R4595.1, U4507.5
X893C7715F557CE9A212C: R4576.1, R4577.1, U4541.1
X955B8D9A3A253B164FE4: R4535.1, U4508.3 (S1), U4539.14
X1227F1DE68A6E7E82DD7: R4596.1, U4507.12
X1264DBD5BF1EA6B5909E: U4523.8, U4523.12, U4523.13
X1696F606406B51CD1BF2: U4519.13, U4536.6 (~Q)
X2781F3EA18C148791B18: U4524.1, U4524.4, U4524.5
X4201C7254D01EFEAE234: R4559.1, R4560.1, U4540.8
X4463C23CE8D19EBA104D: R4544.1, R4547.2, U4509.7, U4512.11
X5230CAFF97DE5D14B821: U4513.6, U4513.10
X5253CC06A0B56536E91A: U4517.6, U4517.9, U4518.4, U4522.1, U4523.10
X6178A6F25F183D1FA28F: C4502.1, U4501.6 (Vout), U4539.3 (+)
X7071EBE878B181AAE681: R4599.2, RB4501.1, U4545.10 (+)
X8975F505244A7B18E41F: U4528.11, U4529.1, U4529.2
X9791E4C8B176990128D8: U4526.9, U4526.10, U4527.13, U4528.13
X28812F18F764B7CD8550: C4508.1, D4504.2 (A), R4532.2, U4512.3
X42321DC477250DD5E139: Q4501.1 (E1), Q4501.4 (E2), U4540.14
X57434BF4C4A2400D5FF7: U4533.2 (D)
X61003EE13806AD930803: U4529.8
X76421D6F8F698545EE98: Q4505.1 (B), Q4505.3 (C), Q4506.1 (B), R4579.1
X92224A3334118B6F54CF: Q4502.1 (B), Q4502.3 (C), Q4503.1 (B), R4562.1
X450878AC1D56C6EA3A8B: R4581.2, R4582.1, U4507.14 (+)
X498820D5B746D4E0C19B: U4523.3, U4523.4, U4523.5
X905685EC1015D0F48FA7: R4519.2, R4520.2, U4509.3 (+)
X974842E79A8A1EAECA9C: C4513.1, R4595.2, R4596.2, R4597.2, R4598.2, U4541.10 (+)
X1343815FFAE28AB97C7F: U4524.3, U4524.12
X3423123E5A42F3C7244E: Q4504.6 (C1), RV4507.2 (Wiper), RV4507.3 (CW), U4541.6 (-)
X28942158ADCDB2051622: R4545.1, R4589.1, U4506.7 (D4), U4509.6 (-), U4545.7
X0606344579E28F515E7B: U4527.3, U4527.4, U4527.12
X08384916135D44050CD6: U4519.12, U4522.10, U4524.2, U4525.1, U4529.9, U4529.10, U4537.9 (Q)
XA3A6F5B8A2E3A348C704: U4526.11, U4527.1, U4527.2
XA6A88CEE713E31E83828: R4545.2, R4546.2, U4510.3 (+)
XA9ADAD20734B26A93D8D: U4526.8, U4527.5, U4528.5
XA0019CBD381390FABFAF: U4524.11
XA097B37821C98E0E3DFB: Q4506.3 (C), R4580.1
XA127A2E75DD869108B50: U4516.10, U4535.6 (~Q)
XA77604BBB1E557ECE2E2: R4593.1, U4506.6 (S4), U4506.11 (S3)
XAA9091685007611E4F89: Q4503.3 (C), R4563.1
XABCD7ED6AB8081A9681F: R4557.1, U4543.13 (-), U4543.14
XAE88D21E883D66941E31: U4523.6, U4523.9
XAF9F10FB975A487DFD86: U4513.8, U4531.2 (D)
XAF227EED7463E583070A: U4533.5 (Q), U4533.12 (D)
XB0A1E968E4F69B5DB855: U4513.11, U4514.1, U4514.2
XB6F69AAB23E388F9646F: U4513.13, U4518.1, U4526.4, U4537.6 (~Q)
XB59A27755DA0DFD9B8F8: U4527.11, U4528.1, U4528.2
XB87DFDEBAA653EEF7611: U4521.6, U4521.9, U4521.10
XB291A24204861F814A90: U4545.13 (-), U4545.14
XBB3ACB3D3BEF839FA424: U4521.3, U4521.13
XBB6AA00E39B76C309D9E: U4513.3, U4513.9
XBD7E3C746F5FE4012F0B: U4530.5 (Q), U4530.12 (D)
XBDF0B621B786D33FF4AD: U4512.4, U4512.5
XBF0338CF4603F9BA5322: R4551.1, U4543.1, U4543.2 (-)
XC0E0F98A26C9CC1C4D6C: R4585.2, R4586.2, U4545.2 (-)
XC0EE167C419B9155F9DB: R4517.1
XC2C3DB6FF0E0375BC0DC: R4541.2, R4542.1, U4510.2 (-)
XC28E977C15ED06CF4B9F: R4593.2, R4594.1, U4507.13 (-)
XC95B2E82DFFA680FFD88: U4520.11, U4521.5
XC650EC11CBBA984A5970: R4535.2, R4536.1, U4539.13 (-)
XC989D40AE1B7C728036B: U4512.6, U4530.1 (~R), U4530.13 (~R)
XC391969CB98E5C497A9F: U4512.12, U4525.2, U4535.12 (D)
XC6387653BA2E7B711606: U4506.16 (IN2), U4528.3
XC702352809EDFD562791: U4505.2 (1B), U4538.5 (Q)
XC37409415891B35F52EA: U4522.6, U4537.12 (D)
XCBBC84AF0F20129EBDE7: R4554.2, R4555.2, U4543.9 (-)
XCBE958EC3A5E759E0B38: D4506.3 (COM), R4573.2, U4544.12 (+)
XCC0F292FF4CAF56BE744: U4516.9, U4517.12, U4520.12, U4524.10, U4526.1, U4526.13, U4529.4, U4529.5, U4536.9 (Q)
XCE1EED7C0EE4E59ED6F5: U4521.11, U4522.2
XCFA56506A863890C4D02: R4571.2, R4572.2, U4544.9 (-)
XCFF560EA12D0022BF7B8: U4524.8, U4524.13
XD5FFD6E3DD1936FC9578: C4511.1, R4549.2, R4550.1, U4543.3 (+)
XD94E94DED6EDAB459E28: R4581.1, RV4508.2 (Wiper)
XD179A1B028A3EA451A2E: R4537.1, R4543.1, R4583.1, U4506.3 (S1), U4506.10 (D3), U4540.1
XD73036DC0A72BAA1A62B: R4520.1, R4521.2, U4509.1, U4512.1
XDA42AB5CE6934988A59F: U4516.4, U4518.5, U4520.1, U4532.9 (Q)
XDA0835E4A421295C0506: Q4501.3 (C2), R4562.2
XDA25847BA9EF23107934: RB4502.2, RB4503.2, RB4504.1, U4545.9 (-)
XDBCAAEF8FCE56591E686: R4586.1, U4506.15 (D2), U4545.1
XDD8714CB850BA1F0D3F8: R4557.2, R4558.2, RV4502.2 (Wiper), RV4502.3 (CW), U4540.9 (-)
XDE12830CCB176AEEC9C0: R4598.1, U4508.14 (S2)
XE0C6D016F1E81EA3CE72: R4533.1, U4512.8, U4530.3 (C), U4530.11 (C), U4531.3 (C), U4531.11 (C), U4532.3 (C), U4532.11 (C), U4533.3 (C), U4533.11 (C), U4534.3 (C), U4534.11 (C), U4535.3 (C), U4535.11 (C), U4536.3 (C), U4536.11 (C), U4537.3 (C), U4537.11 (C), U4538.3 (C)
XE1F0F27AB2CB9DE968A0: R4546.1, R4548.2, U4510.1, U4512.13
XE2AF37ADA464BFF275F4: R4553.1, R4554.1, U4543.7
XE04CC2BECBE997655E3D: U4515.11, U4516.2
XE7FDC1572AFFD74406F6: R4564.2, R4565.1, U4507.4 (-)
XE8EEABDDE8FBB60741D7: U4515.8, U4515.12
XE81BA8626BFFC3F50D24: U4527.6, U4527.9, U4527.10
XE290E6F424FCBA9DE0D5: U4514.5, U4537.8 (~Q)
XE935F353D9D0A09C8244: R4551.2, R4552.2, R4553.2, U4543.6 (-)
XE19211E7777BFD6C5571: U4517.11, U4518.2
XE44423D3AA135C1DE9C4: U4512.2, U4513.1, U4513.2
XE1168244D1DE58C973DA: U4529.6
XEC77FCCDD2CCF2C4DC73: U4516.8, U4516.12, U4516.13
XEC8974AEA8FAA7972572: Q4504.1 (E1), Q4504.4 (E2), U4541.7
XED7D09C8F09F1C63B74B: R4502.1, R4558.1, R4575.1, RV4504.1 (CCW), RV4508.1 (CCW), U4539.7
XED165ED96D75C15A85C4: D4505.2 (K), D4506.2 (K), R4501.1, R4503.1, R4518.1, R4539.1, R4541.1, R4561.1, R4578.1, RB4502.1, RV4504.3 (CW), RV4508.3 (CW), U4510.6 (-), U4539.1, U4539.2 (-), U4539.12 (+), U4540.3 (+)
XEEC4C0A4EDC5D143B410: U4516.6, U4517.2, U4520.10
XF1FD500779FF0E175D20: U4515.3, U4515.13
XF3B0B2A5E7B5801B1B2E: C4512.1, R4566.2, R4567.1, U4544.3 (+)
XF7DF53376150FF0BB2F9: U4520.3, U4520.5, U4521.2
XF8E50EC8D32F5F829903: U4532.5 (Q), U4532.12 (D)
XF57B592E04D51A9BFB35: R4580.2, U4507.16
XF76BE147CC4AD19AE0CC: U4514.13, U4534.6 (~Q)
XF289CB0058E1C5EF70D9: U4518.3, U4519.5
XF40810D5F1B21273DD1A: Q4501.5 (B2), R4560.2
XF69333997B8E2F92DE05: R4552.1
XFA409E521113DBF7BA3F: R4555.1, R4556.1, U4543.8
XFBBF4FE2ED52A893DC14: Q4501.6 (C1), RV4503.2 (Wiper), RV4503.3 (CW), U4540.13 (-)
XFBDD3A378A95D1FD00F5: R4537.2, R4538.1, U4540.2 (-)
XFD67769B873CAFBB4B81: R4574.1, U4544.13 (-), U4544.14
XFE59C363E1D7C42DA3AD: U4521.1, U4537.5 (Q)
