Takazudo/zudo-osc-hole-field/boards/osc-core/sheets/envelope_E6_K.kicad_sch

## KiCad design boards/osc-core/sheets/envelope_E6_K.kicad_sch (2026-10-05)

Schematic: envelope_E6_K.kicad_sch

Parts:
C4601: 1e-07 F; C0603; MPN GRM188R71H104KA93D
C4602: 1e-06 F; C0603
C4608: 1 µF; C0603
C4609: 1 nF C0G; C0603
C4610, C4613: 100 nF C0G; C1206; MPN 1206CG104J500NT; LCSC C46348
C4611, C4612: 1e-08 F; C0603
C4614, C4621, C4622, C4623, C4624, C4625, C4626, C4627, C4628, C4629, C4630, C4631, C4632, C4633, C4634, C4635, C4636, C4637, C4638, C4639, C4640, C4641, C4642, C4643, C4644, C4645, C4646, C4647, C4648, C4649, C4650, C4651, C4652, C4653, C4654, C4655, C4657, C4658, C4659, C4660, C4661, C4662, C4663, C4666, C4667, C4668, C4669, C4670, C4671: 100 nF; C0603; MPN GRM188R71H104KA93D
D4604: BAS16GW-QX; SOD-123; MPN BAS16GW-QX
D4605, D4606: BAT54S,215; SOT-23; MPN BAT54S,215
Q4601, Q4604: BCM847BS,115; SOT-363_SC-70-6; MPN BCM847BS,115
Q4602, Q4603, Q4605, Q4606: MMBT3906,215; SOT-23; MPN MMBT3906,215
R4601, R4602, R4619: 10000 Ω; R0603
R4603: 22000 Ω; R0603
R4604, R4617: 100000 Ω; R0603; MPN RT0603BRD07100KL
R4618: 33200 Ω; R0603
R4620: 390000 Ω; R0603
R4621: 4700 Ω; R0603
R4632, R4636, R4638, R4643, R4645, R4651, R4653, R4654, R4655, R4657, R4668, R4670, R4671, R4672, R4674, R4683, R4684, R4685, R4686, R4687, R4688, R4689, R4690: 100 kΩ; R0603; MPN RT0603BRD07100KL
R4633, R4634: 47 kΩ; R0603
R4635: 60 kΩ; R0603
R4637: 80 kΩ; R0603
R4639: 40 kΩ; R0603
R4640, R4656, R4673: 10 kΩ; R0603
R4641: 79 kΩ; R0603
R4642, R4662, R4663, R4679, R4680: 22 kΩ; R0603
R4644, R4646: 10 MΩ; R0603
R4647, R4648: 4.7 kΩ; R0603
R4649, R4666: 1000 Ω; R0603
R4650, R4667: 1e+07 Ω; R0603
R4652, R4658, R4669, R4675: 200 kΩ; R0603
R4659, R4676: 3.3 kΩ; R0603
R4660, R4665, R4677, R4682, R4692, R4694: 1 kΩ; R0603
R4661, R4678: 300 kΩ; R0603
R4664, R4681: 470 kΩ; R0603
R4691, R4693: 899 kΩ; R0603
R4695, R4696, R4697, R4698: 100 Ω; R0603
R4699: 64 kΩ; R0603
RB4601: 80 kΩ; R0603
RB4602, RB4603: 100 kΩ; R0603; MPN RT0603BRD07100KL
RB4604: 400 kΩ; R0603
RV4602, RV4606: 1 kΩ; Potentiometer_Bourns_TC33X_Vertical; MPN TC33X-2-102E
RV4603, RV4607: 50 kΩ; Potentiometer_Bourns_TC33X_Vertical
RV4604, RV4608: 10 kΩ; Potentiometer_Bourns_TC33X_Vertical; MPN TC33X-2-103E
U4601: REF5050AIDR; SOIC-8_3.9x4.9mm_P1.27mm; MPN REF5050AIDR; LCSC C27804
U4605: CD74HC221M96; SOIC-16_3.9x9.9mm_P1.27mm; MPN CD74HC221M96; LCSC C133954
U4606, U4608: ADG5412FBRUZ; TSSOP-16_4.4x5mm_P0.65mm; MPN ADG5412FBRUZ; LCSC C579073
U4607: LM13700M/NOPB; SOIC-16_3.9x9.9mm_P1.27mm; MPN LM13700M/NOPB; LCSC C1346265
U4609, U4610: LM393BIDR; SOIC-8_3.9x4.9mm_P1.27mm; MPN LM393BIDR
U4612: SN74HC14DR; SOIC-14_3.9x8.7mm_P1.27mm; MPN SN74HC14DR
U4613, U4614, U4615, U4616, U4617, U4618, U4619, U4620, U4621, U4622, U4623, U4624, U4625, U4626, U4627, U4628, U4629: SN74HC00DR; SOIC-14_3.9x8.7mm_P1.27mm; MPN SN74HC00DR
U4630, U4631, U4632, U4633, U4634, U4635, U4636, U4637, U4638: SN74HC74DR; SOIC-14_3.9x8.7mm_P1.27mm; MPN SN74HC74DR
U4639, U4640, U4641: OPA4197IPWR; TSSOP-14_4.4x5mm_P0.65mm; MPN OPA4197IPWR; LCSC C2057327
U4643, U4644, U4645: OPA4196IDR; SOIC-14_3.9x8.7mm_P1.27mm; MPN OPA4196IDR; LCSC C2057385

Connections:
+5V: C4621.1, C4630.1, C4631.1, C4632.1, C4633.1, C4634.1, C4635.1, C4636.1, C4637.1, C4638.1, C4639.1, C4640.1, C4641.1, C4642.1, C4643.1, C4644.1, C4645.1, C4646.1, C4647.1, C4648.1, C4649.1, C4650.1, C4651.1, C4652.1, C4653.1, C4654.1, C4655.1, C4657.1, D4604.1 (K), R4621.1, R4632.1, R4634.1, R4647.1, R4648.1, U4605.16 (VCC), U4612.14 (VCC), U4613.14 (VCC), U4614.14 (VCC), U4615.14 (VCC), U4616.14 (VCC), U4617.14 (VCC), U4618.14 (VCC), U4619.14 (VCC), U4620.14 (VCC), U4621.14 (VCC), U4622.14 (VCC), U4623.14 (VCC), U4624.14 (VCC), U4625.14 (VCC), U4626.14 (VCC), U4627.14 (VCC), U4628.14 (VCC), U4629.14 (VCC), U4630.2 (D), U4630.4 (~S), U4630.10 (~S), U4630.14 (VCC), U4631.4 (~S), U4631.10 (~S), U4631.14 (VCC), U4632.4 (~S), U4632.10 (~S), U4632.14 (VCC), U4633.4 (~S), U4633.10 (~S), U4633.14 (VCC), U4634.4 (~S), U4634.10 (~S), U4634.14 (VCC), U4635.4 (~S), U4635.10 (~S), U4635.14 (VCC), U4636.4 (~S), U4636.10 (~S), U4636.14 (VCC), U4637.4 (~S), U4637.10 (~S), U4637.14 (VCC), U4638.4 (~S), U4638.10 (~S), U4638.14 (VCC)
+12V: C4601.1, C4614.1, C4622.1, C4624.1, C4626.1, C4628.1, C4629.1, C4658.1, C4660.1, C4662.1, C4666.1, C4668.1, C4670.1, Q4602.2 (E), Q4603.2 (E), Q4605.2 (E), Q4606.2 (E), U4601.2 (Vin), U4606.13 (VDD), U4607.11 (V+), U4608.13 (VDD), U4609.8 (V+), U4610.8 (V+), U4639.4 (V+), U4640.4 (V+), U4641.4 (V+), U4643.4 (V+), U4644.4 (V+), U4645.4 (V+)
-12V: C4623.1, C4625.1, C4627.1, C4659.1, C4661.1, C4663.1, C4667.1, C4669.1, C4671.1, U4606.4 (VSS), U4607.6 (V-), U4608.4 (VSS), U4639.11 (V-), U4640.11 (V-), U4641.11 (V-), U4643.11 (V-), U4644.11 (V-), U4645.11 (V-)
AGND: C4601.2, C4602.2, C4608.2, C4609.2, C4611.2, C4612.2, C4613.2, C4614.2, C4621.2, C4622.2, C4623.2, C4624.2, C4625.2, C4626.2, C4627.2, C4628.2, C4629.2, C4630.2, C4631.2, C4632.2, C4633.2, C4634.2, C4635.2, C4636.2, C4637.2, C4638.2, C4639.2, C4640.2, C4641.2, C4642.2, C4643.2, C4644.2, C4645.2, C4646.2, C4647.2, C4648.2, C4649.2, C4650.2, C4651.2, C4652.2, C4653.2, C4654.2, C4655.2, C4657.2, C4658.2, C4659.2, C4660.2, C4661.2, C4662.2, C4663.2, C4666.2, C4667.2, C4668.2, C4669.2, C4670.2, C4671.2, D4605.1 (A), D4606.1 (A), Q4601.2 (B1), Q4604.2 (B1), R4604.2, R4636.2, R4638.2, R4640.2, R4642.2, R4650.2, R4665.2, R4667.2, R4682.2, R4684.2, R4690.2, R4692.2, R4694.2, RB4601.2, RB4604.2, U4601.4 (GND), U4605.1 (1A), U4605.8 (GND), U4605.9 (2A), U4605.10 (2B), U4605.11 (2R), U4606.5 (GND), U4607.7, U4607.10, U4608.5 (GND), U4608.6 (S4), U4608.7 (D4), U4608.8 (IN4), U4608.9 (IN3), U4608.10 (D3), U4608.11 (S3), U4608.15 (D2), U4609.4 (GND), U4610.4 (GND), U4610.5 (+), U4612.7 (GND), U4613.7 (GND), U4614.7 (GND), U4615.7 (GND), U4616.7 (GND), U4617.7 (GND), U4618.7 (GND), U4619.7 (GND), U4620.7 (GND), U4621.7 (GND), U4622.7 (GND), U4623.7 (GND), U4624.7 (GND), U4625.7 (GND), U4626.7 (GND), U4627.7 (GND), U4628.7 (GND), U4629.7 (GND), U4629.12, U4629.13, U4630.7 (GND), U4631.7 (GND), U4632.7 (GND), U4633.7 (GND), U4634.7 (GND), U4635.7 (GND), U4636.7 (GND), U4637.7 (GND), U4638.7 (GND), U4638.11 (C), U4638.12 (D), U4638.13 (~R), U4639.5 (+), U4640.10 (+), U4640.12 (+), U4641.3 (+), U4641.5 (+), U4641.12 (+), U4643.5 (+), U4643.10 (+), U4644.5 (+), U4644.10 (+), U4645.12 (+)
X0A74CE0CE83152B5270C: R4696.1, U4607.12
X00BF5622D64D21A15AC7: U4629.6
X1A56FAC2909B66A3BA00: Q4604.6 (C1), RV4607.2 (Wiper), RV4607.3 (CW), U4641.6 (-)
X1BE2FF37952DFBC34086: U4619.8, U4637.2 (D)
X1C5DF1E81ABC49BDC155: R4697.1, U4608.2 (D1)
X1FE658DC41C02D3E7ABF: U4620.11, U4621.5
X1FEE0A4C237E6AF293D4: U4618.11, U4619.1, U4619.2
X2A4BBA3EC3B88C680084: U4606.1 (IN1), U4627.8
X2AF11D6E7FB4948BDEA2: U4616.9, U4617.12, U4620.12, U4624.10, U4626.1, U4626.13, U4629.4, U4629.5, U4636.9 (Q)
X2B7E8791C7A625ADDC55: U4613.8, U4631.2 (D)
X2D3A9D379EFA19E37232: U4641.13 (-), U4641.14
X2DB474D60A6F8B245F08: U4615.8, U4615.12
X2E75E5A88690FD256B4E: Q4604.3 (C2), R4679.2
X3C6C687468640B6EF5FD: R4663.2, U4607.1
X3D9DB9D8CDF65F493A37: U4633.2 (D)
X3FCEE2BB385C8F4829D5: R4668.2, R4669.2, R4670.2, U4644.6 (-)
X4A09F1C0C01093819B38: U4623.6, U4623.9
X04B0332874B6A751EBF2: R4654.2, R4655.2, U4643.9 (-)
X4F8053C7D4A25D690146: U4624.8, U4624.13
X5C144BBBD6B3BE44357E: RB4602.2, RB4603.2, RB4604.1, U4645.9 (-)
X5CCC23E65DBB399D35F6: C4602.1, U4601.6 (Vout), U4639.3 (+)
X5DCC494C4F63F17CFE89: U4608.1 (IN1), U4626.6
X5E935C6FC1C6009BD9A6: U4605.2 (1B), U4638.5 (Q)
X6A9059CC356C6554DD97: U4616.10, U4635.6 (~Q)
X6E9FB4BAEA3FF68C1948: U4613.12, U4636.8 (~Q)
X6E646CB5B4FD67AFB14D: R4602.1, R4658.1, R4675.1, RV4604.1 (CCW), RV4608.1 (CCW), U4639.7
X7B09F18FE4C23E910BD8: U4615.3, U4615.13
X7D3EE40D5296DD82B4F0: U4619.13, U4636.6 (~Q)
X7DD72B6BBDD299CD84F8: R4695.1, U4607.5
X7E96F378B3BBF96C3FE9: R4683.2, R4684.1, U4645.3 (+)
X7F502E64ECD955242189: C4610.1, R4634.2, U4605.15 (1RXCX)
X8A7D7D29E8DC52F3CE4A: R4649.1
X8A58565164C7AD5DB771: U4613.4, U4613.5
X08AB1FE396D2383E44F4: U4624.1, U4624.4, U4624.5
X8ACD1E503E37BABF7C27: R4637.2, R4638.1, U4640.2 (-)
X8AF626288EC5C4B5F0B4: U4624.6, U4624.9
X8F6CFA1028403B20A819: R4686.1, U4606.15 (D2), U4645.1
X8FF3B793C6218A596E54: U4635.9 (Q), U4636.2 (D)
X09A10D70C19C7AE738E3: U4632.5 (Q), U4632.12 (D)
X9B24D85652D0E6A4A818: R4652.1
X9BF4A3E68949EBBE3EDC: U4618.3, U4619.5
X9F4D8DA650FEE0C736BA: U4608.16 (IN2), U4625.11
X9F61A7055EEEA35F62E7: R4685.1, R4687.1, R4699.1, U4641.8, U4641.9 (-)
X9F414E24159D28B3D92D: U4617.8, U4636.12 (D)
X11E2E2197431C27F8588: R4617.2, R4618.2, U4609.2 (-)
X12EE115501367E86F96E: R4691.1, U4606.2 (D1), U4606.14 (S2)
X15A31970A06D461453EF: R4669.1
X21B52C3773C6B29B4BA5: U4614.11, U4616.1
X27A3D281F84F12F70A45: R4620.1, R4621.2, U4609.1, U4612.1
X28A0DC809DA9EBE04BB4: Q4604.5 (B2), R4677.2
X28A6E7AF0E6FCA41C358: U4625.8, U4625.12
X36FEF502916B0681FF9C: U4622.8, U4622.12, U4622.13
X45C9091F706AFD0A887F: R4617.1
X50AA63E1E846168D2F13: U4628.11, U4629.1, U4629.2
X50CD99E115A009B45E1F: U4627.6, U4627.9, U4627.10
X58BA9FC206DDF943A6B8: U4612.4, U4612.5
X059EB93D00CE2AC55BF0: U4628.6, U4628.9, U4628.10
X64B9B6F8BD80E3164D0D: R4603.2, R4604.1, U4639.10 (+)
X067BC0557E1F6D979C15: R4655.1, R4656.1, U4643.8
X069AA41BCE4A36C26FB2: U4605.4 (1Q), U4615.1, U4615.2
X73EA3F1C2B5B29CB8065: U4619.3, U4619.4
X75E2097BD6AB8D07260A: Q4601.6 (C1), RV4603.2 (Wiper), RV4603.3 (CW), U4640.13 (-)
X76A4EC7A9FD3DE8ADC75: R4671.2, R4672.2, U4644.9 (-)
X79CF4150C4AC57A865CE: C4608.1, D4604.2 (A), R4632.2, U4612.3
X80DBFAF19158A3B6365D: R4698.1, U4608.14 (S2)
X88F1EF3CE73F96642CD0: R4657.2, R4658.2, RV4602.2 (Wiper), RV4602.3 (CW), U4640.9 (-)
X98B5F48F9B41E7A6B783: U4619.12, U4622.10, U4624.2, U4625.1, U4629.9, U4629.10, U4637.9 (Q)
X134A4D0C981AB6EE8EA7: U4606.16 (IN2), U4628.3
X155A309ECA0E13DB5004: U4621.1, U4637.5 (Q)
X159B55ACEDAEF88DC328: U4616.4, U4618.5, U4620.1, U4632.9 (Q)
X0218E96EEBACF63E2EE3: U4624.3, U4624.12
X369F9AE084A2E21F04B2: R4619.2, R4620.2, U4609.3 (+)
X397FF51868343A219B35: R4678.2, RV4607.1 (CCW)
X399EFF0A3423A9B7F8BB: U4612.10, U4626.2, U4634.12 (D)
X509D39C9F3AFFB5111C7: U4619.11, U4621.4
X559C73BAEFBA482B820C: U4626.3, U4626.5
X574A3A13DBE94F92FD36: U4618.8, U4618.12
X0627A6EDB06A5778D373: U4614.8, U4615.5
X636D4AFFCE971DBB6DDC: R4664.2, R4665.1, U4607.4 (-)
X732F670D07DA1B1966CD: U4612.6, U4630.1 (~R), U4630.13 (~R)
X758D88EDF0020334C609: U4633.5 (Q), U4633.12 (D)
X760D073316B6E4F8D3DD: R4633.1, U4612.8, U4630.3 (C), U4630.11 (C), U4631.3 (C), U4631.11 (C), U4632.3 (C), U4632.11 (C), U4633.3 (C), U4633.11 (C), U4634.3 (C), U4634.11 (C), U4635.3 (C), U4635.11 (C), U4636.3 (C), U4636.11 (C), U4637.3 (C), U4637.11 (C), U4638.3 (C)
X830C2BB63DBD75F71763: U4615.11, U4616.2
X921DE9E457C3B4A52802: U4616.6, U4617.2, U4620.10
X934D1D52CBF505174B51: Q4603.3 (C), R4663.1
X954EF2E4A58935BC01BB: R4651.2, R4652.2, R4653.2, U4643.6 (-)
X959F04EC80920D580426: U4615.6, U4615.9, U4615.10
X7346F5D084A2538727AA: U4621.8, U4621.12
X9403AFEA4B6A1DC7C7D8: U4634.9 (Q), U4635.2 (D)
X12782F4CC53A52368452: R4639.2, R4640.1, U4640.5 (+)
X20704F48A56B6CBF76A2: U4617.11, U4618.2
X26272F1B8A7A8B10EEE9: R4635.2, R4636.1, U4639.13 (-)
X44525CE19DAF5E8C78D3: U4622.6, U4637.12 (D)
X68994E3A9D4102609CCD: U4625.3, U4625.13
X479764B836FB7BB3EF48: U4632.2 (D)
X970238DF6CCA2103EC2D: R4641.2, R4642.1, U4610.2 (-)
X2385958A6C741D943468: U4617.6, U4617.9, U4618.4, U4622.1, U4623.10
X4748694DBB0668C4653E: U4623.11, U4638.2 (D)
X5909484C66EAAD701C00: C4611.1, R4649.2, R4650.1, U4643.3 (+)
X81661675DED6E82682D1: U4626.9, U4626.10, U4627.13, U4628.13
X440024921E7CC815755E: C4610.2, U4605.14 (1CX)
X13973266902E4C17EDA8: R4676.2, RV4606.1 (CCW)
X5792542747712B37C23F: R4645.2, R4646.2, U4610.3 (+)
XA1D6CC2B12D4194D2E9D: R4661.2, RV4603.1 (CCW)
XA1E42AB55FC8AF34F9BB: U4612.12, U4625.2, U4635.12 (D)
XA2BA81EE8F1F6E2D322A: U4626.8, U4627.5, U4628.5
XA3CBF51EA09C202FB5CA: U4616.8, U4616.12, U4616.13
XA5A6F732A11E9F6B007A: R4644.1, R4647.2, U4609.7, U4612.11
XA8CDFCBD3749F8D6EEB0: U4626.11, U4627.1, U4627.2
XA29B9734AD5692A8301A: U4616.5, U4631.8 (~Q)
XA34ABC1E8C32CE20DE3D: Q4601.3 (C2), R4662.2
XA66FFDFC9CD56E21A61D: R4643.2, R4644.2, U4609.5 (+)
XA86F732E3D7677B19F91: R4691.2, R4692.1, U4607.3 (+)
XA99EFB5E345EBFD3A416: R4688.1, U4640.6 (-), U4640.7
XA263F42C65E26BD665B2: U4612.2, U4613.1, U4613.2
XA530EB1BB78FC7BC3938: U4615.4, U4633.9 (Q)
XA7576D403245C8CFB20B: R4674.1, U4644.13 (-), U4644.14
XA9988E9FEA5BD9096C03: Q4606.3 (C), R4680.1
XA83717DFE85A1843AF54: U4624.11
XA889187DBDF9DD63F4F8: Q4601.5 (B2), R4660.2
XA939497E35731780CC52: R4670.1, R4671.1, U4644.7
XAB9FD3F48A14D59B72B3: Q4602.1 (B), Q4602.3 (C), Q4603.1 (B), R4662.1
XAB9375A43A8DCB4460A2: R4651.1, U4643.1, U4643.2 (-)
XAB25959C10192BADCD9D: U4620.8, U4620.13
XAE9C4A74BA9D11176F35: R4657.1, U4643.13 (-), U4643.14
XAF57F77AD8505F2AB3D3: D4605.3 (COM), R4656.2, U4643.12 (+)
XB2BD1E07121D76138C04: R4668.1, U4644.1, U4644.2 (-)
XB02C8D332566FAFD22C0: U4614.13, U4634.6 (~Q)
XB2CBBB9BB15D4679BB34: U4631.5 (Q), U4631.12 (D)
XB021D009020E77DFDAD4: U4617.13, U4620.4, U4635.5 (Q)
XB47A774AF73EDC116715: Q4605.1 (B), Q4605.3 (C), Q4606.1 (B), R4679.1
XB74D3E33882D9505BF03: U4606.8 (IN4), U4629.3
XB569B3DF9CBC2CB83C0B: R4645.1, R4689.1, U4606.7 (D4), U4609.6 (-), U4645.7
XB847DB1D9196D85019DE: R4676.1, R4677.1, U4641.1
XB53267D4410FFA502740: U4617.3, U4617.10
XBA81B496A3E9398FD1C9: U4623.8, U4623.12, U4623.13
XBB5F6C7036C61029F9A4: C4609.1, R4633.2, U4612.9
XBB45BC46992241005930: U4622.11, U4623.1, U4628.4, U4628.12
XBC704272DE5AAB19D5C2: R4601.2, R4602.2, U4639.6 (-)
XBD7CA4E4EDE3AEC072C4: R4635.1, U4608.3 (S1), U4639.14
XBD0757D16BB59A3B55D6: U4620.3, U4620.5, U4621.2
XBD1606A50AF671F381AD: U4606.9 (IN3), U4628.8
XBDDD54D6289047857CFE: R4653.1, R4654.1, U4643.7
XBE5D53BB312CDAE0ECE1: U4614.6, U4614.9, U4614.10, U4625.5
XBF4CAE21EB1896F69BA3: R4693.2, R4694.1, U4607.13 (-)
XC1E91BF45463428233E7: U4623.3, U4623.4, U4623.5
XC6EB2B5A48007AF42474: R4646.1, R4648.2, U4610.1, U4612.13
XC8FD72C56E0857408282: R4672.1, R4673.1, U4644.8
XC22E458B0CC1481C514F: D4605.2 (K), D4606.2 (K), R4601.1, R4603.1, R4618.1, R4639.1, R4641.1, R4661.1, R4678.1, RB4602.1, RV4604.3 (CW), RV4608.3 (CW), U4610.6 (-), U4639.1, U4639.2 (-), U4639.12 (+), U4640.3 (+)
XC47DA59E758EDC72527F: U4618.6, U4618.9, U4618.10
XC359F771F4A81BCAB123: U4623.2, U4636.5 (Q)
XC219257FF6AF093163AA: R4680.2, U4607.16
XC762654D1B87FD609A8C: U4627.11, U4628.1, U4628.2
XCAEFFFBEFDBA63E45A5C: U4622.3, U4622.4, U4622.5
XCC272F39F31DBA17BDDB: Q4604.1 (E1), Q4604.4 (E2), U4641.7
XCD43A30AEB9FF3D433C3: U4616.11, U4617.1
XCD870FFA181056ADF64D: U4619.6, U4619.9, U4619.10
XCDCBAEFD05258FC8B756: U4613.11, U4614.1, U4614.2
XCFD32A6DD12EDD7B70B1: U4613.3, U4613.9
XD8C3B34CC595E213CF3B: U4614.5, U4637.8 (~Q)
XD61A734562E1889B57F0: U4645.13 (-), U4645.14
XD80723D237EB4E072716: C4612.1, R4666.2, R4667.1, U4644.3 (+)
XDAA5776AE72BE078D30E: R4659.1, R4660.1, U4640.8
XDCF170EFBBCE9B652E6D: R4689.2, R4690.1, U4645.6 (-)
XDECF1DD3AF5E9CD6CD36: R4619.1, U4639.8, U4639.9 (-)
XDEF38C61030C3CB97057: U4614.3, U4614.4
XE0CCF29B1B7AD12B34E4: R4681.1, RV4608.2 (Wiper)
XE2F0D8A9D1A0D6FE7C81: U4625.6, U4625.9, U4625.10
XE4E1513DE79627D3BBC3: R4666.1
XE07BBB971EDFFE4FD240: U4605.3 (1R), U4622.9, U4625.4, U4626.12, U4630.9 (Q), U4631.1 (~R), U4631.13 (~R), U4632.1 (~R), U4632.13 (~R), U4633.1 (~R), U4633.13 (~R), U4634.1 (~R), U4634.13 (~R), U4635.1 (~R), U4635.13 (~R), U4636.1 (~R), U4636.13 (~R), U4637.1 (~R), U4637.13 (~R), U4638.1 (~R)
XE7D53C05CFFF63ED18FC: U4621.3, U4621.13
XE7DD63E61E1F3AD1E652: C4613.1, R4695.2, R4696.2, R4697.2, R4698.2, U4641.10 (+)
XE8F2DB9E4B93B56F3FFF: R4659.2, RV4602.1 (CCW)
XE9ACCFE49C60EC22E908: R4664.1, RV4604.2 (Wiper)
XE11F310AFADC2AC47D5B: U4621.6, U4621.9, U4621.10
XE12A1C0728D038D1B249: R4693.1, U4606.6 (S4), U4606.11 (S3)
XE36E38C2F0FCFC617A0D: Q4601.1 (E1), Q4601.4 (E2), U4640.14
XE892D1C4313D8B3D50DA: R4687.2, R4688.2, U4645.5 (+)
XE21582D444A555A63BEB: R4681.2, R4682.1, U4607.14 (+)
XE81531DE199582BE1344: U4629.8
XEB516E4D36E1987BE634: R4637.1, R4643.1, R4683.1, U4606.3 (S1), U4606.10 (D3), U4640.1
XEBADF49433D187353003: R4674.2, R4675.2, RV4606.2 (Wiper), RV4606.3 (CW), U4641.2 (-)
XF5F6B467F497E9483A4A: U4621.11, U4622.2
XF86B7087E00BA7383783: U4613.6, U4613.10
XF13580F441B47AF4967B: R4685.2, R4686.2, U4645.2 (-)
XF99902CE5290D966C9C8: R4699.2, RB4601.1, U4645.10 (+)
XF8501438038B000DD39C: U4614.12, U4618.13, U4620.2, U4631.9 (Q), U4634.2 (D)
XF581209630535499288A: D4606.3 (COM), R4673.2, U4644.12 (+)
XFA4AFBF858BC014C5597: U4630.5 (Q), U4630.12 (D)
XFA778DAA8F2041395702: U4616.3, U4617.4, U4617.5
XFABBAF1457B5C9697AED: U4620.6, U4620.9
XFBEB96A166B093F8B966: U4627.3, U4627.4, U4627.12
XFBFE7BE3D8ED3A77CE22: RB4603.1, U4645.8
XFFBCF756A1D9E25D0693: U4613.13, U4618.1, U4626.4, U4637.6 (~Q)
