Takazudo/zudo-osc-hole-field/boards/osc-core/sheets/filter_F1_K.kicad_sch

## KiCad design boards/osc-core/sheets/filter_F1_K.kicad_sch (2026-10-05)

Schematic: filter_F1_K.kicad_sch

Parts:
C2101: 1e-07 F; C0603; MPN GRM188R71H104KA93D
C2102: 1e-06 F; C0603
C2103, C2106, C2109: 1e-10 F; C0603; MPN C0603C101J5GACTU
C2104, C2107, C2110: 1e-11 F; C0603
C2105, C2108, C2111: 1e-08 F; C0603
C2112, C2113: 150 pF C0G; C0603
C2114, C2115: 100 pF; C0603; MPN C0603C101J5GACTU
C2116, C2125, C2126, C2127, C2128, C2129, C2130, C2131, C2132, C2133, C2134, C2135, C2136, C2137, C2138, C2139, C2140, C2141, C2142, C2143, C2144, C2145, C2146: 100 nF; C0603; MPN GRM188R71H104KA93D
D2105, D2107: BAT54S,215; SOT-23; MPN BAT54S,215
D2106, D2108, D2109, D2110, D2111, D2112, D2113, D2114, D2115, D2116, D2117, D2118, D2119, D2120, D2121, D2122, D2123, D2124: BAS16GW-QX; SOD-123; MPN BAS16GW-QX
Q2101: BCM847BS,115; SOT-363_SC-70-6; MPN BCM847BS,115
Q2102, Q2103, Q2104, Q2105, Q2106: MMBT3906,215; SOT-23; MPN MMBT3906,215
R2101, R2102, R2122, R2130, R2138: 10000 Ω; R0603
R2103: 22000 Ω; R0603
R2104, R2125, R2126, R2133, R2134, R2141, R2142: 100000 Ω; R0603; MPN RT0603BRD07100KL
R2121, R2129, R2137: 100 Ω; R0603
R2123, R2127, R2131, R2135, R2139, R2143: 1000 Ω; R0603
R2124, R2128, R2132, R2136, R2140, R2144: 1e+07 Ω; R0603
R2145, R2158: 50 kΩ; R0603
R2146, R2147, R2148, R2149, R2159, R2160, R2161, R2162, R2166, R2170, R2174, R2178, R2179, R2180, R2181, R2182, R2183, R2184, R2186, R2187, R2191, R2192, R2193, R2194, R2195, R2197, R2198: 100 kΩ; R0603; MPN RT0603BRD07100KL
R2150: 1.3 kΩ; R0603
R2151, R2165, R2169, R2173, R2177: 1 kΩ; R0603
R2152: 300 kΩ; R0603
R2153, R2154, R2155, R2190: 22 kΩ; R0603
R2156: 40 kΩ; R0603
R2157, R2185, R2189, R2196: 10 kΩ; R0603
R2163, R2167, R2171, R2175: 200 Ω; R0603
R2164, R2168, R2172, R2176: 470 kΩ; R0603
R2188: 49.9 kΩ; R0603
R2199: 12.4 kΩ; R0603
RB2101: 10 kΩ; R0603
RB2102: 22 kΩ; R0603
RB2103: 330 kΩ; R0603
RB2104: 100 kΩ; R0603; MPN RT0603BRD07100KL
RB2105: 68.1 kΩ; R0603
RV2107: 1 kΩ; Potentiometer_Bourns_TC33X_Vertical; MPN TC33X-2-102E
RV2108: 50 kΩ; Potentiometer_Bourns_TC33X_Vertical
RV2109, RV2110, RV2111, RV2112: 10 kΩ; Potentiometer_Bourns_TC33X_Vertical; MPN TC33X-2-103E
RV2113: 500 kΩ; Potentiometer_Bourns_TC33X_Vertical
U2101: REF5050AIDR; SOIC-8_3.9x4.9mm_P1.27mm; MPN REF5050AIDR; LCSC C27804
U2106, U2107: LM13700M/NOPB; SOIC-16_3.9x9.9mm_P1.27mm; MPN LM13700M/NOPB; LCSC C1346265
U2108, U2109: OPA4197IPWR; TSSOP-14_4.4x5mm_P0.65mm; MPN OPA4197IPWR; LCSC C2057327
U2110, U2111, U2112, U2113, U2114, U2115, U2116: OPA4196IDR; SOIC-14_3.9x8.7mm_P1.27mm; MPN OPA4196IDR; LCSC C2057385

Connections:
+12V: C2101.1, C2116.1, C2125.1, C2127.1, C2129.1, C2131.1, C2133.1, C2135.1, C2137.1, C2139.1, C2141.1, C2143.1, C2145.1, Q2102.2 (E), Q2103.2 (E), Q2104.2 (E), U2101.2 (Vin), U2106.11 (V+), U2107.11 (V+), U2108.4 (V+), U2109.4 (V+), U2110.4 (V+), U2111.4 (V+), U2112.4 (V+), U2113.4 (V+), U2114.4 (V+), U2115.4 (V+), U2116.4 (V+)
-12V: C2126.1, C2128.1, C2130.1, C2132.1, C2134.1, C2136.1, C2138.1, C2140.1, C2142.1, C2144.1, C2146.1, U2106.6 (V-), U2107.6 (V-), U2108.11 (V-), U2109.11 (V-), U2110.11 (V-), U2111.11 (V-), U2112.11 (V-), U2113.11 (V-), U2114.11 (V-), U2115.11 (V-), U2116.11 (V-)
AGND: C2101.2, C2102.2, C2105.2, C2108.2, C2111.2, C2112.2, C2113.2, C2116.2, C2125.2, C2126.2, C2127.2, C2128.2, C2129.2, C2130.2, C2131.2, C2132.2, C2133.2, C2134.2, C2135.2, C2136.2, C2137.2, C2138.2, C2139.2, C2140.2, C2141.2, C2142.2, C2143.2, C2144.2, C2145.2, C2146.2, D2105.1 (A), D2107.1 (A), Q2101.2 (B1), R2104.2, R2124.2, R2128.2, R2132.2, R2136.2, R2140.2, R2144.2, R2157.2, R2163.2, R2165.2, R2167.2, R2169.2, R2171.2, R2173.2, R2175.2, R2177.2, R2179.2, U2101.4 (GND), U2106.7, U2106.10, U2107.7, U2107.10, U2108.5 (+), U2108.12 (+), U2109.3 (+), U2109.5 (+), U2109.10 (+), U2109.12 (+), U2112.5 (+), U2113.5 (+), U2113.10 (+), U2114.10 (+), U2114.12 (+), U2115.12 (+), U2116.3 (+), U2116.5 (+), U2116.10 (+), U2116.12 (+)
X0FFCEF74D6E2F530B0EE: R2158.2, R2159.2, R2160.2, R2161.2, U2112.9 (-)
X1BE457125B299BD637D5: D2114.1 (K), D2115.2 (A)
X1BFC8B1AE1FA8255A87E: R2170.2, R2171.1, U2107.3 (+)
X1C2AF7372EA6114E111A: R2178.2, R2179.1, U2114.3 (+), U2115.5 (+)
X1D7C13EF0F0429C157CA: R2123.1
X1F3BE2B0C54B7392AAD2: R2135.1
X1FEC31E39975DA90F6FA: D2122.2 (A), D2123.1 (K)
X3B8A3CBCACE3F3286E5C: R2101.2, R2102.2, U2108.6 (-)
X3FDB5C3A9C702DA3237E: R2172.1, RV2111.2 (Wiper)
X4A6785F32FA620155F2F: R2186.1, U2113.13 (-), U2113.14
X4E72DCDEE1BB544B05D0: D2118.2 (A), D2119.1 (K)
X4EC41A4E212075F1D8FF: R2193.1, R2194.1, U2114.8
X4F69606D71FB72217ADA: Q2101.5 (B2), R2151.2
X05BB99476651FDA55DD2: R2195.1, R2196.1, U2114.14
X5BE69E7747A8BBD8827F: U2116.6 (-), U2116.7
X6A6FC9F60F23B7329630: C2104.2, R2125.2, R2126.2, U2110.6 (-)
X6AC22A3DBBEB03BD4DAB: R2150.2, RV2107.1 (CCW)
X6F25CE4F7EF477D117FE: R2168.2, R2169.1, U2106.13 (-)
X07A2B1AEB127E3940533: D2105.3 (COM), R2185.2, U2113.12 (+)
X7C5F17AED66F7138F3A8: R2159.1, U2113.1, U2113.2 (-)
X7CEF15A4DB002837A875: R2164.1, RV2109.2 (Wiper)
X07E18B65AC397793EEFD: R2182.1, R2183.1, U2113.7
X7F52A3A75BAC03DFC565: R2152.2, RV2108.1 (CCW)
X8A7D8F94CE75F7D1333C: R2155.2, U2106.16
X8E57EA6C655A2898766F: Q2102.1 (B), Q2102.3 (C), Q2103.1 (B), Q2104.1 (B), R2153.1
X9A591EC2CF76B3860AE6: Q2101.6 (C1), RV2108.2 (Wiper), RV2108.3 (CW), U2109.2 (-)
X9ACC125DBB43F274DA2F: R2197.2, R2198.2, U2115.6 (-)
X9B265340AB0E3ED7A9D8: D2106.2 (A), Q2105.1 (B), R2189.2
X9D4DAF35CDBF61FFC354: RB2105.1, U2116.1
X9D48783F6C0BDBE5292E: C2107.1, R2134.1, R2181.1, U2111.1
X9F48AB794328450B093A: R2191.2, R2192.2, R2193.2, U2114.9 (-)
X9F48F5CCE05B92C29E4F: U2116.8, U2116.9 (-)
X16B589CCC71D86F8F685: R2150.1, R2151.1, U2108.14
X20F583943AD176D65E4E: D2109.1 (K), D2110.2 (A)
X022D2D07D4909D62AA5A: R2198.1, U2115.7, U2115.10 (+)
X32FB315F9B615526523A: R2172.2, R2173.1, U2107.4 (-)
X39CF37EA61B7349ADBED: C2109.1, R2137.1, U2111.8
X47F5D9307ADE3C04E05C: R2164.2, R2165.1, U2106.4 (-)
X47F88BF45C5E2E011545: R2137.2, R2138.1
X64F573E990879850AB21: C2115.1, RB2101.1, U2115.8
X71FE9D19F3BAD5E1F9CA: R2168.1, RV2110.2 (Wiper)
X81CA071E9915CC31EAEA: R2158.1, R2166.1, R2170.1, U2112.13 (-), U2112.14
X82DACB5D97927516216B: R2176.1, RV2112.2 (Wiper)
X84B6328EA318F70A06F5: R2184.1, R2185.1, U2113.8
X92D58D65DA2819F30731: R2131.1
X97E728989B7553A387AE: R2125.1, U2110.3 (+)
X97ED0B30E9679E8FC3C2: R2121.2, R2122.1
X098AE4DB4AFDC4994323: U2109.13 (-), U2109.14
X0237D255CD9D7C13F289: D2121.2 (A), D2122.1 (K)
X292FDC39C2768F1CC745: D2107.3 (COM), R2196.2, U2115.3 (+)
X419E27ECCE370EBEF72E: D2116.1 (K), D2124.2 (A), RV2113.2 (Wiper), RV2113.3 (CW), U2107.5, U2115.13 (-)
X528B810E4A83D402C734: R2186.2, R2187.2, U2114.2 (-)
X632AF8DD6216ED26A96D: R2141.1, U2111.10 (+)
X662A9C63225394F5D218: R2187.1, U2114.1, U2114.5 (+)
X669F7F55E51EC338DD7B: Q2104.3 (C), R2155.1
X707EFEF7CDB3E09D13A9: C2104.1, R2126.1, R2146.1, U2110.7
X713D2A205A347A93E088: D2115.1 (K), D2116.2 (A)
X766DEFBB808A3B44DE63: C2106.2, R2130.2, U2110.13 (-)
X777AE553F61985D2B279: C2115.2, D2108.1 (K), Q2106.2 (E), R2199.2, U2115.9 (-)
X827AEA950E231EF8E99E: D2119.2 (A), D2120.1 (K)
X945AEADF88F2C93BB341: D2111.1 (K), D2112.2 (A)
X987A3E4AA963B1C8AA04: R2180.1, U2111.6 (-), U2111.7
X5786DA3A2B61D0A46B7F: R2143.1
X6193B39FF0D3BAAE2096: R2174.2, R2175.1, U2107.13 (-)
X7183CCEDEAABA18363B5: R2133.1, U2110.12 (+)
X8291DE54C2D65D346B6A: Q2106.3 (C), RB2102.1
X9149CF71445CABA980B6: R2139.2, R2140.1, U2111.12 (+)
X9767C64E126DEDB6653C: R2127.1
X13516CD8BD8A7B0DD5BA: RB2102.2, U2107.16
X17548F34273A3429C2C2: C2103.1, R2121.1, U2110.1
X033527C992D537BBC155: R2176.2, R2177.1, U2107.14 (+)
X059078D8342235F11DC1: R2190.2, U2107.1
X81320A62027112B50CB2: R2129.2, R2130.1
X3149377C3AC6C3F8E3BE: RB2103.2, RV2113.1 (CCW)
X4619731F6D6CD500DC9A: C2110.1, R2142.1, R2192.1, U2111.14
X6143095ACEB7FB1CAC83: U2109.8, U2109.9 (-)
X6594459FB89E835432A8: RB2105.2, U2107.12, U2116.2 (-)
X502245311C7C4A244DB4: D2117.2 (A), D2118.1 (K)
XA6ED170526F374EF262B: D2108.2 (A), Q2106.1 (B), RB2101.2
XA82AFE6CDE755FEB4702: D2105.2 (K), D2107.2 (K), R2101.1, R2103.1, R2152.1, R2178.1, R2188.1, R2199.1, RV2109.3 (CW), RV2110.3 (CW), RV2111.3 (CW), RV2112.3 (CW), U2108.1, U2108.2 (-)
XA3808316751BA419D842: R2156.1, R2174.1
XADF88CCD1C7010B28E03: U2116.13 (-), U2116.14
XAFE03CD37A28E84342B3: R2197.1, U2115.1, U2115.2 (-)
XB2F6FC20D1E21C4537F7: R2139.1
XB3B77A184C93E1CC345A: R2123.2, R2124.1, U2110.5 (+)
XB6E668DA222909AB8B8B: C2110.2, R2141.2, R2142.2, U2111.13 (-)
XBC9C9596195D55C2BF05: C2108.1, R2135.2, R2136.1, U2111.5 (+)
XBD0A69C8299F563C8B99: C2102.1, U2101.6 (Vout), U2108.3 (+)
XBFAEC0612B7FC6F40234: D2113.1 (K), D2114.2 (A)
XC6ECCF70E51867F704FA: D2110.1 (K), D2111.2 (A)
XC714CBDAC502D1241627: R2145.2, R2146.2, R2147.2, R2148.2, U2112.6 (-)
XC47289B2D63E8F79DF30: R2149.2, RV2107.2 (Wiper), RV2107.3 (CW), U2108.13 (-)
XC56799B1E6CC255795DD: R2162.2, R2163.1, U2106.3 (+)
XC699649CE0269BC8B120: R2154.2, U2106.1
XC5025765F7BDD89F24FA: R2102.1, R2147.1, RV2109.1 (CCW), RV2110.1 (CCW), RV2111.1 (CCW), RV2112.1 (CCW), U2108.7
XCCC9D10E8EA5D047DC8D: C2105.1, R2127.2, R2128.1, U2110.10 (+)
XD57A711995FB4DF0F18E: D2109.2 (A), D2117.1 (K), RB2104.2
XD5934A6383AC6B2194E1: R2145.1, U2110.8, U2110.9 (-)
XD7093B7E2131BCA8A130: D2112.1 (K), D2113.2 (A)
XD7960B3C1A6276C15CB0: C2112.1, U2106.5, U2112.12 (+)
XD924657C1582E82F5B20: C2114.1, R2189.1, U2114.7
XDA44BC0C8571D66EBED8: C2107.2, R2133.2, R2134.2, U2111.2 (-)
XDC8C662F5B1440D78217: U2108.8, U2108.9 (-)
XDC35A1AED1ECB087343C: R2156.2, R2157.1, U2112.10 (+)
XDFC4A44FA72B3E433EB7: R2194.2, R2195.2, U2114.13 (-)
XE6D2BC37D1C3343F1F55: R2131.2, R2132.1, U2111.3 (+)
XE9B8955E3D0FFC2A8E6B: R2191.1, U2112.1, U2112.2 (-)
XE9D0A410E750A9A7D5D7: Q2103.3 (C), R2154.1
XE81DCCD63340C32994FE: R2161.1, R2162.1, U2112.8
XE870A8797CFDCFA73D75: D2123.2 (A), D2124.1 (K)
XE2909C2985AF1A84E0D4: D2120.2 (A), D2121.1 (K)
XE12439D03E337D23AC24: Q2101.1 (E1), Q2101.4 (E2), U2109.1
XE90052769FEECEF6F632: U2109.6 (-), U2109.7
XE3846894359ECD4DE16C: C2106.1, R2129.1, U2110.14
XEC565E32A16AE130A8F8: C2114.2, D2106.1 (K), Q2105.2 (E), R2188.2, U2114.6 (-)
XEE2F0DC139F055AF581F: Q2101.3 (C2), R2153.2
XEEE4DCAB22B9FEDF41B4: R2180.2, R2181.2, R2182.2, U2113.6 (-)
XF0F6C146C6CBE9DF56D6: R2166.2, R2167.1, U2106.14 (+)
XF6DF87CBE4C9C7E6A800: R2183.2, R2184.2, U2113.9 (-)
XF9A2118DE14C361E157B: R2160.1, RB2103.1, RB2104.1, U2115.14
XF63CC87AF9AAA847655C: C2113.1, U2106.12, U2113.3 (+)
XF63093E46E8C33187045: R2103.2, R2104.1, U2108.10 (+)
XFA9DCB7DBECAB01B4CCC: Q2105.3 (C), R2190.1
XFBA2993367865ABF5102: C2109.2, R2138.2, U2111.9 (-)
XFC49685B028E7B16216C: R2148.1, R2149.1, U2112.7
XFCE33F8014B0156831A0: C2111.1, R2143.2, R2144.1, U2112.3 (+)
XFF546AF26171B59F9FB3: C2103.2, R2122.2, U2110.2 (-)
