Takazudo/zudo-osc-hole-field/boards/osc-core/sheets/filter_F2_K.kicad_sch

## KiCad design boards/osc-core/sheets/filter_F2_K.kicad_sch (2026-10-05)

Schematic: filter_F2_K.kicad_sch

Parts:
C2201: 1e-07 F; C0603; MPN GRM188R71H104KA93D
C2202: 1e-06 F; C0603
C2203, C2206, C2209: 1e-10 F; C0603; MPN C0603C101J5GACTU
C2204, C2207, C2210: 1e-11 F; C0603
C2205, C2208, C2211: 1e-08 F; C0603
C2212, C2213: 150 pF C0G; C0603
C2214, C2215: 100 pF; C0603; MPN C0603C101J5GACTU
C2216, C2225, C2226, C2227, C2228, C2229, C2230, C2231, C2232, C2233, C2234, C2235, C2236, C2237, C2238, C2239, C2240, C2241, C2242, C2243, C2244, C2245, C2246: 100 nF; C0603; MPN GRM188R71H104KA93D
D2205, D2207: BAT54S,215; SOT-23; MPN BAT54S,215
D2206, D2208, D2209, D2210, D2211, D2212, D2213, D2214, D2215, D2216, D2217, D2218, D2219, D2220, D2221, D2222, D2223, D2224: BAS16GW-QX; SOD-123; MPN BAS16GW-QX
Q2201: BCM847BS,115; SOT-363_SC-70-6; MPN BCM847BS,115
Q2202, Q2203, Q2204, Q2205, Q2206: MMBT3906,215; SOT-23; MPN MMBT3906,215
R2201, R2202, R2222, R2230, R2238: 10000 Ω; R0603
R2203: 22000 Ω; R0603
R2204, R2225, R2226, R2233, R2234, R2241, R2242: 100000 Ω; R0603; MPN RT0603BRD07100KL
R2221, R2229, R2237: 100 Ω; R0603
R2223, R2227, R2231, R2235, R2239, R2243: 1000 Ω; R0603
R2224, R2228, R2232, R2236, R2240, R2244: 1e+07 Ω; R0603
R2245, R2258: 50 kΩ; R0603
R2246, R2247, R2248, R2249, R2259, R2260, R2261, R2262, R2266, R2270, R2274, R2278, R2279, R2280, R2281, R2282, R2283, R2284, R2286, R2287, R2291, R2292, R2293, R2294, R2295, R2297, R2298: 100 kΩ; R0603; MPN RT0603BRD07100KL
R2250: 1.3 kΩ; R0603
R2251, R2265, R2269, R2273, R2277: 1 kΩ; R0603
R2252: 300 kΩ; R0603
R2253, R2254, R2255, R2290: 22 kΩ; R0603
R2256: 40 kΩ; R0603
R2257, R2285, R2289, R2296: 10 kΩ; R0603
R2263, R2267, R2271, R2275: 200 Ω; R0603
R2264, R2268, R2272, R2276: 470 kΩ; R0603
R2288: 49.9 kΩ; R0603
R2299: 12.4 kΩ; R0603
RB2201: 10 kΩ; R0603
RB2202: 22 kΩ; R0603
RB2203: 330 kΩ; R0603
RB2204: 100 kΩ; R0603; MPN RT0603BRD07100KL
RB2205: 68.1 kΩ; R0603
RV2207: 1 kΩ; Potentiometer_Bourns_TC33X_Vertical; MPN TC33X-2-102E
RV2208: 50 kΩ; Potentiometer_Bourns_TC33X_Vertical
RV2209, RV2210, RV2211, RV2212: 10 kΩ; Potentiometer_Bourns_TC33X_Vertical; MPN TC33X-2-103E
RV2213: 500 kΩ; Potentiometer_Bourns_TC33X_Vertical
U2201: REF5050AIDR; SOIC-8_3.9x4.9mm_P1.27mm; MPN REF5050AIDR; LCSC C27804
U2206, U2207: LM13700M/NOPB; SOIC-16_3.9x9.9mm_P1.27mm; MPN LM13700M/NOPB; LCSC C1346265
U2208, U2209: OPA4197IPWR; TSSOP-14_4.4x5mm_P0.65mm; MPN OPA4197IPWR; LCSC C2057327
U2210, U2211, U2212, U2213, U2214, U2215, U2216: OPA4196IDR; SOIC-14_3.9x8.7mm_P1.27mm; MPN OPA4196IDR; LCSC C2057385

Connections:
+12V: C2201.1, C2216.1, C2225.1, C2227.1, C2229.1, C2231.1, C2233.1, C2235.1, C2237.1, C2239.1, C2241.1, C2243.1, C2245.1, Q2202.2 (E), Q2203.2 (E), Q2204.2 (E), U2201.2 (Vin), U2206.11 (V+), U2207.11 (V+), U2208.4 (V+), U2209.4 (V+), U2210.4 (V+), U2211.4 (V+), U2212.4 (V+), U2213.4 (V+), U2214.4 (V+), U2215.4 (V+), U2216.4 (V+)
-12V: C2226.1, C2228.1, C2230.1, C2232.1, C2234.1, C2236.1, C2238.1, C2240.1, C2242.1, C2244.1, C2246.1, U2206.6 (V-), U2207.6 (V-), U2208.11 (V-), U2209.11 (V-), U2210.11 (V-), U2211.11 (V-), U2212.11 (V-), U2213.11 (V-), U2214.11 (V-), U2215.11 (V-), U2216.11 (V-)
AGND: C2201.2, C2202.2, C2205.2, C2208.2, C2211.2, C2212.2, C2213.2, C2216.2, C2225.2, C2226.2, C2227.2, C2228.2, C2229.2, C2230.2, C2231.2, C2232.2, C2233.2, C2234.2, C2235.2, C2236.2, C2237.2, C2238.2, C2239.2, C2240.2, C2241.2, C2242.2, C2243.2, C2244.2, C2245.2, C2246.2, D2205.1 (A), D2207.1 (A), Q2201.2 (B1), R2204.2, R2224.2, R2228.2, R2232.2, R2236.2, R2240.2, R2244.2, R2257.2, R2263.2, R2265.2, R2267.2, R2269.2, R2271.2, R2273.2, R2275.2, R2277.2, R2279.2, U2201.4 (GND), U2206.7, U2206.10, U2207.7, U2207.10, U2208.5 (+), U2208.12 (+), U2209.3 (+), U2209.5 (+), U2209.10 (+), U2209.12 (+), U2212.5 (+), U2213.5 (+), U2213.10 (+), U2214.10 (+), U2214.12 (+), U2215.12 (+), U2216.3 (+), U2216.5 (+), U2216.10 (+), U2216.12 (+)
X0A7C2A84D94F69C74B08: C2214.2, D2206.1 (K), Q2205.2 (E), R2288.2, U2214.6 (-)
X0ACA9FAE16CB353A0CB1: R2256.1, R2274.1
X0AE9B4A13FF5E987C450: R2294.2, R2295.2, U2214.13 (-)
X0B81EC1382DF80CE950C: D2209.1 (K), D2210.2 (A)
X0C0F1AAC75510740701C: C2202.1, U2201.6 (Vout), U2208.3 (+)
X0CD1ED6D76016EE72D17: R2250.1, R2251.1, U2208.14
X1DF34FFFB923D70D6AC5: C2208.1, R2235.2, R2236.1, U2211.5 (+)
X1E371B08558E40B24207: D2208.2 (A), Q2206.1 (B), RB2201.2
X2A46965047837A866FAB: R2272.2, R2273.1, U2207.4 (-)
X2B8C723FAF2E6F75DE16: R2291.1, U2212.1, U2212.2 (-)
X2BB3BCC65027A0717EFD: Q2203.3 (C), R2254.1
X2C92E9C6C0DE3ABEF992: U2209.8, U2209.9 (-)
X02DEAED0334D82205F6C: R2268.2, R2269.1, U2206.13 (-)
X2E63525FBBE899E17DBA: R2233.1, U2210.12 (+)
X2EE25A6F6AE743F3C858: U2209.13 (-), U2209.14
X3A032E49047B6AB9FECC: R2231.2, R2232.1, U2211.3 (+)
X3A55588AF008358260C5: R2291.2, R2292.2, R2293.2, U2214.9 (-)
X4D7539335EB2ABC435DB: U2209.6 (-), U2209.7
X4EDEC3DE200932292870: Q2202.1 (B), Q2202.3 (C), Q2203.1 (B), Q2204.1 (B), R2253.1
X4F32EE2195C42F89E923: R2283.2, R2284.2, U2213.9 (-)
X5BF6FE0DDAEF34E3DEB1: D2222.2 (A), D2223.1 (K)
X05EA213DF230394CB24A: C2210.2, R2241.2, R2242.2, U2211.13 (-)
X6E54CD1D97BEE3726D81: C2203.1, R2221.1, U2210.1
X7E292A5147B8AD5AB240: C2209.1, R2237.1, U2211.8
X7EED3C2496125C7B4C01: R2231.1
X8DA2DF97B8E580A14065: C2207.1, R2234.1, R2281.1, U2211.1
X9BC55CB24132DBE1E40E: R2202.1, R2247.1, RV2209.1 (CCW), RV2210.1 (CCW), RV2211.1 (CCW), RV2212.1 (CCW), U2208.7
X9F175A89D847BE3F6D46: R2239.1
X9FAC1CEEB96BE0F3CE9E: R2293.1, R2294.1, U2214.8
X10F7DEF7DC2E86C6C743: R2276.1, RV2212.2 (Wiper)
X24E3C16307B2FAA35477: R2223.1
X25C6508F0D450BB21F57: D2210.1 (K), D2211.2 (A)
X26D9FA7B94A8BC8254BB: R2239.2, R2240.1, U2211.12 (+)
X30AAC3AC50DA91BD6FED: C2205.1, R2227.2, R2228.1, U2210.10 (+)
X34C003B95F51E457536E: R2272.1, RV2211.2 (Wiper)
X37A266B88A7FAFA3F6B3: R2270.2, R2271.1, U2207.3 (+)
X41CE30224279DEA816B2: C2207.2, R2233.2, R2234.2, U2211.2 (-)
X42B724700E97F5FE129B: R2278.2, R2279.1, U2214.3 (+), U2215.5 (+)
X44F96DB5F077899D1E6B: D2219.2 (A), D2220.1 (K)
X50AFEB2FDCC02AAF8C6D: D2221.2 (A), D2222.1 (K)
X50F46481DA5C7AA8A140: C2206.2, R2230.2, U2210.13 (-)
X52E9ABADE2847C655125: U2216.8, U2216.9 (-)
X056B4CC99FD47B93EDCC: R2243.1
X63E8AE879DAC769786BA: Q2205.3 (C), R2290.1
X65E952248FA7DF68F858: R2264.1, RV2209.2 (Wiper)
X76DC968B8FB090DB980A: D2206.2 (A), Q2205.1 (B), R2289.2
X78EF9D04BC1BBC685DF1: R2250.2, RV2207.1 (CCW)
X81AE9767B60B482E7C92: R2252.2, RV2208.1 (CCW)
X83B52BFA0A0D2B53849E: R2280.1, U2211.6 (-), U2211.7
X85E738180F5C70F1A457: R2227.1
X91A6564EAD50D748C178: R2295.1, R2296.1, U2214.14
X92A00452E6478B79234F: R2201.2, R2202.2, U2208.6 (-)
X0217C1908B493DF05710: R2297.2, R2298.2, U2215.6 (-)
X263E1A73EDF3DD056650: R2286.1, U2213.13 (-), U2213.14
X384FDC6CB36A886ACA15: R2255.2, U2206.16
X419C4916FF5B54E2AC89: R2261.1, R2262.1, U2212.8
X488AAFFF511AD69D06C9: R2245.2, R2246.2, R2247.2, R2248.2, U2212.6 (-)
X489C344A609BF5655EC0: C2204.1, R2226.1, R2246.1, U2210.7
X817DDA86FD198C4775BA: C2206.1, R2229.1, U2210.14
X3470B64811CEDC9F86E6: Q2201.6 (C1), RV2208.2 (Wiper), RV2208.3 (CW), U2209.2 (-)
X4084EF9D5FBD756DA299: R2203.2, R2204.1, U2208.10 (+)
X04362CFBD4589662DE61: Q2206.3 (C), RB2202.1
X05209FC6E4D7D0F1C4DB: R2258.2, R2259.2, R2260.2, R2261.2, U2212.9 (-)
X5654AD6D3086D9EBB30E: RB2203.2, RV2213.1 (CCW)
X7985B0752A3E34339F44: R2225.1, U2210.3 (+)
X14032E90D3FFE6A1D4BB: R2297.1, U2215.1, U2215.2 (-)
X29854AE733C2B74B98B6: D2214.1 (K), D2215.2 (A)
X59559A656156E7CC3239: D2220.2 (A), D2221.1 (K)
X64750EAD045B08CFF878: R2259.1, U2213.1, U2213.2 (-)
X86381E411CC3FBBEEADE: C2209.2, R2238.2, U2211.9 (-)
X94210EAC11BB98036631: R2258.1, R2266.1, R2270.1, U2212.13 (-), U2212.14
X479485ED622DC6D107DB: R2223.2, R2224.1, U2210.5 (+)
X935179E83B5542EE5948: R2280.2, R2281.2, R2282.2, U2213.6 (-)
X3555296AEA387E6710A2: R2266.2, R2267.1, U2206.14 (+)
X7781688F337E7FCA1ED8: R2298.1, U2215.7, U2215.10 (+)
X13984600BFB786AD48D5: C2211.1, R2243.2, R2244.1, U2212.3 (+)
X83505917C4B7487D1CE9: R2221.2, R2222.1
X90814404C6CCD1671A40: R2284.1, R2285.1, U2213.8
X97465823FD4E374650CD: R2287.1, U2214.1, U2214.5 (+)
X532980813DED35791CED: R2235.1
X55193054118CBB7C36A9: RB2202.2, U2207.16
X0104308636188EFAB72F: C2214.1, R2289.1, U2214.7
XA1A27364576BA36DE8F0: R2254.2, U2206.1
XA43D9910ABB9C5D8EBAA: R2249.2, RV2207.2 (Wiper), RV2207.3 (CW), U2208.13 (-)
XABA79B312C27AF9FA5E2: D2205.3 (COM), R2285.2, U2213.12 (+)
XAEADCEC87692C9052698: R2290.2, U2207.1
XB0F4B125230F68C75889: C2203.2, R2222.2, U2210.2 (-)
XB8C1560A7570DC7A2B7C: D2217.2 (A), D2218.1 (K)
XB9D2A914247B25F8994C: R2241.1, U2211.10 (+)
XB59E7321FE52B7E42F81: U2216.13 (-), U2216.14
XB5789DD069AA94B00B59: R2276.2, R2277.1, U2207.14 (+)
XB171028B3A2E5623EE74: U2208.8, U2208.9 (-)
XC96AF414792F98AAF501: C2213.1, U2206.12, U2213.3 (+)
XC577C90964B31152E727: Q2201.3 (C2), R2253.2
XC1149D74CCC833EBF9A8: D2216.1 (K), D2224.2 (A), RV2213.2 (Wiper), RV2213.3 (CW), U2207.5, U2215.13 (-)
XC19387F5B49A211AD2BD: D2205.2 (K), D2207.2 (K), R2201.1, R2203.1, R2252.1, R2278.1, R2288.1, R2299.1, RV2209.3 (CW), RV2210.3 (CW), RV2211.3 (CW), RV2212.3 (CW), U2208.1, U2208.2 (-)
XC36004EDAFB86F42B8A0: R2229.2, R2230.1
XC64057E2FE5B31FE0D56: R2286.2, R2287.2, U2214.2 (-)
XCAE2D2A29EAB829BEF30: D2212.1 (K), D2213.2 (A)
XCC60712D7624BE0D3176: D2218.2 (A), D2219.1 (K)
XCD7A4E7A63372C01E73B: Q2204.3 (C), R2255.1
XCD48B6C77859C58E4BB5: R2264.2, R2265.1, U2206.4 (-)
XCDDA6C558DA382D7DA2D: R2268.1, RV2210.2 (Wiper)
XD3CEE2EB863745D21DF2: D2209.2 (A), D2217.1 (K), RB2204.2
XD5D8187BC1393684367F: R2256.2, R2257.1, U2212.10 (+)
XD41ED59EAF5CBDE30ACD: R2245.1, U2210.8, U2210.9 (-)
XD65D67A1A49D0232C1FE: R2274.2, R2275.1, U2207.13 (-)
XD87E19FBE8221812838D: C2215.2, D2208.1 (K), Q2206.2 (E), R2299.2, U2215.9 (-)
XD986AE545AB102D9A4BA: R2248.1, R2249.1, U2212.7
XDC1F4E8E59CEF641BC50: R2262.2, R2263.1, U2206.3 (+)
XE3CCE6B3C9722D631642: R2260.1, RB2203.1, RB2204.1, U2215.14
XE29CB30E5F799014D8FE: D2223.2 (A), D2224.1 (K)
XE308A046FDC844C6F4AF: C2210.1, R2242.1, R2292.1, U2211.14
XE787F73A6DD02BA3A17E: U2216.6 (-), U2216.7
XE4850AB4E84CF0A5E191: C2204.2, R2225.2, R2226.2, U2210.6 (-)
XE07191B4BC9097E50F9C: C2212.1, U2206.5, U2212.12 (+)
XEE7B0858542E575543AD: D2211.1 (K), D2212.2 (A)
XF0C92B68052EB7564B75: Q2201.1 (E1), Q2201.4 (E2), U2209.1
XF54F143041F12F7463B0: Q2201.5 (B2), R2251.2
XF114FCC8B218E1013F4D: R2237.2, R2238.1
XF178B2F5DF6F782E4440: RB2205.2, U2207.12, U2216.2 (-)
XF4867E6F4E50FBF66540: D2215.1 (K), D2216.2 (A)
XF7997335C6AA753BC906: C2215.1, RB2201.1, U2215.8
XFB369A0F20CC5F0B533B: R2282.1, R2283.1, U2213.7
XFBD81EB4423EDA37C16F: RB2205.1, U2216.1
XFCAE054D8BCBB6128119: D2213.1 (K), D2214.2 (A)
XFD24B5E71BBEE9405689: D2207.3 (COM), R2296.2, U2215.3 (+)
