Takazudo/zudo-osc-hole-field/boards/osc-core/sheets/filter_F3_K.kicad_sch

## KiCad design boards/osc-core/sheets/filter_F3_K.kicad_sch (2026-10-05)

Schematic: filter_F3_K.kicad_sch

Parts:
C2301: 1e-07 F; C0603; MPN GRM188R71H104KA93D
C2302: 1e-06 F; C0603
C2303, C2306, C2309: 1e-10 F; C0603; MPN C0603C101J5GACTU
C2304, C2307, C2310: 1e-11 F; C0603
C2305, C2308, C2311: 1e-08 F; C0603
C2312, C2313: 150 pF C0G; C0603
C2314, C2315: 100 pF; C0603; MPN C0603C101J5GACTU
C2316, C2325, C2326, C2327, C2328, C2329, C2330, C2331, C2332, C2333, C2334, C2335, C2336, C2337, C2338, C2339, C2340, C2341, C2342, C2343, C2344, C2345, C2346: 100 nF; C0603; MPN GRM188R71H104KA93D
D2305, D2307: BAT54S,215; SOT-23; MPN BAT54S,215
D2306, D2308, D2309, D2310, D2311, D2312, D2313, D2314, D2315, D2316, D2317, D2318, D2319, D2320, D2321, D2322, D2323, D2324: BAS16GW-QX; SOD-123; MPN BAS16GW-QX
Q2301: BCM847BS,115; SOT-363_SC-70-6; MPN BCM847BS,115
Q2302, Q2303, Q2304, Q2305, Q2306: MMBT3906,215; SOT-23; MPN MMBT3906,215
R2301, R2302, R2322, R2330, R2338: 10000 Ω; R0603
R2303: 22000 Ω; R0603
R2304, R2325, R2326, R2333, R2334, R2341, R2342: 100000 Ω; R0603; MPN RT0603BRD07100KL
R2321, R2329, R2337: 100 Ω; R0603
R2323, R2327, R2331, R2335, R2339, R2343: 1000 Ω; R0603
R2324, R2328, R2332, R2336, R2340, R2344: 1e+07 Ω; R0603
R2345, R2358: 50 kΩ; R0603
R2346, R2347, R2348, R2349, R2359, R2360, R2361, R2362, R2366, R2370, R2374, R2378, R2379, R2380, R2381, R2382, R2383, R2384, R2386, R2387, R2391, R2392, R2393, R2394, R2395, R2397, R2398: 100 kΩ; R0603; MPN RT0603BRD07100KL
R2350: 1.3 kΩ; R0603
R2351, R2365, R2369, R2373, R2377: 1 kΩ; R0603
R2352: 300 kΩ; R0603
R2353, R2354, R2355, R2390: 22 kΩ; R0603
R2356: 40 kΩ; R0603
R2357, R2385, R2389, R2396: 10 kΩ; R0603
R2363, R2367, R2371, R2375: 200 Ω; R0603
R2364, R2368, R2372, R2376: 470 kΩ; R0603
R2388: 49.9 kΩ; R0603
R2399: 12.4 kΩ; R0603
RB2301: 10 kΩ; R0603
RB2302: 22 kΩ; R0603
RB2303: 330 kΩ; R0603
RB2304: 100 kΩ; R0603; MPN RT0603BRD07100KL
RB2305: 68.1 kΩ; R0603
RV2307: 1 kΩ; Potentiometer_Bourns_TC33X_Vertical; MPN TC33X-2-102E
RV2308: 50 kΩ; Potentiometer_Bourns_TC33X_Vertical
RV2309, RV2310, RV2311, RV2312: 10 kΩ; Potentiometer_Bourns_TC33X_Vertical; MPN TC33X-2-103E
RV2313: 500 kΩ; Potentiometer_Bourns_TC33X_Vertical
U2301: REF5050AIDR; SOIC-8_3.9x4.9mm_P1.27mm; MPN REF5050AIDR; LCSC C27804
U2306, U2307: LM13700M/NOPB; SOIC-16_3.9x9.9mm_P1.27mm; MPN LM13700M/NOPB; LCSC C1346265
U2308, U2309: OPA4197IPWR; TSSOP-14_4.4x5mm_P0.65mm; MPN OPA4197IPWR; LCSC C2057327
U2310, U2311, U2312, U2313, U2314, U2315, U2316: OPA4196IDR; SOIC-14_3.9x8.7mm_P1.27mm; MPN OPA4196IDR; LCSC C2057385

Connections:
+12V: C2301.1, C2316.1, C2325.1, C2327.1, C2329.1, C2331.1, C2333.1, C2335.1, C2337.1, C2339.1, C2341.1, C2343.1, C2345.1, Q2302.2 (E), Q2303.2 (E), Q2304.2 (E), U2301.2 (Vin), U2306.11 (V+), U2307.11 (V+), U2308.4 (V+), U2309.4 (V+), U2310.4 (V+), U2311.4 (V+), U2312.4 (V+), U2313.4 (V+), U2314.4 (V+), U2315.4 (V+), U2316.4 (V+)
-12V: C2326.1, C2328.1, C2330.1, C2332.1, C2334.1, C2336.1, C2338.1, C2340.1, C2342.1, C2344.1, C2346.1, U2306.6 (V-), U2307.6 (V-), U2308.11 (V-), U2309.11 (V-), U2310.11 (V-), U2311.11 (V-), U2312.11 (V-), U2313.11 (V-), U2314.11 (V-), U2315.11 (V-), U2316.11 (V-)
AGND: C2301.2, C2302.2, C2305.2, C2308.2, C2311.2, C2312.2, C2313.2, C2316.2, C2325.2, C2326.2, C2327.2, C2328.2, C2329.2, C2330.2, C2331.2, C2332.2, C2333.2, C2334.2, C2335.2, C2336.2, C2337.2, C2338.2, C2339.2, C2340.2, C2341.2, C2342.2, C2343.2, C2344.2, C2345.2, C2346.2, D2305.1 (A), D2307.1 (A), Q2301.2 (B1), R2304.2, R2324.2, R2328.2, R2332.2, R2336.2, R2340.2, R2344.2, R2357.2, R2363.2, R2365.2, R2367.2, R2369.2, R2371.2, R2373.2, R2375.2, R2377.2, R2379.2, U2301.4 (GND), U2306.7, U2306.10, U2307.7, U2307.10, U2308.5 (+), U2308.12 (+), U2309.3 (+), U2309.5 (+), U2309.10 (+), U2309.12 (+), U2312.5 (+), U2313.5 (+), U2313.10 (+), U2314.10 (+), U2314.12 (+), U2315.12 (+), U2316.3 (+), U2316.5 (+), U2316.10 (+), U2316.12 (+)
X0AC68F7F43D274064EE6: U2309.13 (-), U2309.14
X0AF8112B69C7244B1EA0: C2307.1, R2334.1, R2381.1, U2311.1
X0C3D24C947A0B5F3EB50: D2310.1 (K), D2311.2 (A)
X0E1F625927BE5B28F9E8: U2309.8, U2309.9 (-)
X0E46085A51B44D50938C: R2339.2, R2340.1, U2311.12 (+)
X0F25C1B40E73B6D42E31: R2386.1, U2313.13 (-), U2313.14
X1B3090AB0FF67D94225B: C2310.1, R2342.1, R2392.1, U2311.14
X1BCBF31DD3DC71C75B3F: C2308.1, R2335.2, R2336.1, U2311.5 (+)
X1BF430DFDDEBDA9D44AA: C2311.1, R2343.2, R2344.1, U2312.3 (+)
X1C1F785A6974DFC14AF1: R2395.1, R2396.1, U2314.14
X1F1A855A4AE2E5F824EC: R2380.2, R2381.2, R2382.2, U2313.6 (-)
X1F9004624E9A0CE2D22A: R2366.2, R2367.1, U2306.14 (+)
X2BDA3C82FA877B0424E9: Q2304.3 (C), R2355.1
X2F7F192BBAEF5BD8A311: R2325.1, U2310.3 (+)
X3E878F04FD5D6F7D46EF: D2309.2 (A), D2317.1 (K), RB2304.2
X3EAF04BE3C453068A5AE: U2308.8, U2308.9 (-)
X5A748C9F10BC16D9ED6F: RB2305.1, U2316.1
X5C75482E648F44663866: C2309.1, R2337.1, U2311.8
X6A0E7F592D0262C057D6: D2321.2 (A), D2322.1 (K)
X6B198689616F45B6B0B3: R2352.2, RV2308.1 (CCW)
X6C1BAF63B063E45615E2: U2316.6 (-), U2316.7
X6D197039CFE02B335E55: R2331.2, R2332.1, U2311.3 (+)
X8B7446D18278CED44922: D2312.1 (K), D2313.2 (A)
X8BDF2BAD2449627A6AD6: R2358.1, R2366.1, R2370.1, U2312.13 (-), U2312.14
X8D097FC3EE080878BFAC: R2343.1
X8D99A0FD5C4292A9C637: D2311.1 (K), D2312.2 (A)
X9ACF5F6547B3FA762225: R2376.2, R2377.1, U2307.14 (+)
X9C0A8E56A9E15E0751A4: R2368.2, R2369.1, U2306.13 (-)
X9CEFF7BBDBDFBCF913B1: R2303.2, R2304.1, U2308.10 (+)
X9E94C8A02F7DD6DDD76E: C2314.2, D2306.1 (K), Q2305.2 (E), R2388.2, U2314.6 (-)
X9ED526F9C81AF9E87774: D2309.1 (K), D2310.2 (A)
X9F7D653AF2B7E248C875: R2327.1
X16F03E11D8F608E0F0C7: RB2305.2, U2307.12, U2316.2 (-)
X17E9433F014659A8D02F: R2378.2, R2379.1, U2314.3 (+), U2315.5 (+)
X18D5886012D3CD3C858B: RB2303.2, RV2313.1 (CCW)
X19B8E3DE6F5DBFB20738: R2386.2, R2387.2, U2314.2 (-)
X31C86FA79F4108C494D9: C2314.1, R2389.1, U2314.7
X33A21456F99AD2970DEB: C2313.1, U2306.12, U2313.3 (+)
X38A5EB5ED9724350ABEA: R2397.2, R2398.2, U2315.6 (-)
X39C38672C471F7713929: R2382.1, R2383.1, U2313.7
X42A840C53C1A214F7CF4: R2391.1, U2312.1, U2312.2 (-)
X45FB1DBD813314DE52D1: C2304.2, R2325.2, R2326.2, U2310.6 (-)
X53FCF9300F387476AB8A: Q2301.3 (C2), R2353.2
X0055FA200D03E4C96010: R2356.2, R2357.1, U2312.10 (+)
X57B93596FBB4F73E6549: R2391.2, R2392.2, R2393.2, U2314.9 (-)
X62E5FBA80218D5E75710: C2309.2, R2338.2, U2311.9 (-)
X64B8A61607D5791A56B8: R2394.2, R2395.2, U2314.13 (-)
X67A892779E12E40231B5: D2322.2 (A), D2323.1 (K)
X72DAD8887E4EF74A9FB7: D2323.2 (A), D2324.1 (K)
X91D7FB7B3C74A3368139: R2393.1, R2394.1, U2314.8
X93B51A3CD40492429370: R2368.1, RV2310.2 (Wiper)
X289D1300CDAB3C2C26D5: U2316.13 (-), U2316.14
X369DFC43E512306E93D9: R2364.2, R2365.1, U2306.4 (-)
X0481D75728108870DDEE: D2315.1 (K), D2316.2 (A)
X588ADD76C2D4F051CB26: R2397.1, U2315.1, U2315.2 (-)
X599D6F008ACD4AF9DBB6: R2329.2, R2330.1
X643E64A807825CB8A359: D2308.2 (A), Q2306.1 (B), RB2301.2
X650F58942AE2A6F0E0CA: RB2302.2, U2307.16
X747E2425D8E401256190: U2309.6 (-), U2309.7
X763F0E8947660083B6D1: R2355.2, U2306.16
X766FABC78DDF445DEF43: R2345.1, U2310.8, U2310.9 (-)
X800D23429C778122F4A1: R2372.2, R2373.1, U2307.4 (-)
X849EE8C41DE7382BA070: R2335.1
X864F97CEE7B087E4EA58: C2306.2, R2330.2, U2310.13 (-)
X878F2A279999CCD4A075: R2361.1, R2362.1, U2312.8
X956FBC959E8122F31870: C2303.2, R2322.2, U2310.2 (-)
X973A72A8410D1AB72B77: R2350.1, R2351.1, U2308.14
X1180C1A9B9B7538FDA64: R2362.2, R2363.1, U2306.3 (+)
X3833DA0E2047F401FB91: R2348.1, R2349.1, U2312.7
X5270B2A325DCFA73F65F: R2339.1
X8865BFEB7A8BC769197A: R2350.2, RV2307.1 (CCW)
X21277E53CF9685D0C806: R2376.1, RV2312.2 (Wiper)
X60576C8696C047840E23: Q2305.3 (C), R2390.1
X188642D0B061DD680F91: C2315.2, D2308.1 (K), Q2306.2 (E), R2399.2, U2315.9 (-)
X235805FBDE65FEABD919: R2333.1, U2310.12 (+)
X605550DA0F4163738709: C2306.1, R2329.1, U2310.14
X01880830AEBFD53EB774: C2305.1, R2327.2, R2328.1, U2310.10 (+)
X5034420C569627042FA5: C2307.2, R2333.2, R2334.2, U2311.2 (-)
X5844954045B5A7447CB6: C2310.2, R2341.2, R2342.2, U2311.13 (-)
XA97F2AF13F60125770D7: R2360.1, RB2303.1, RB2304.1, U2315.14
XA182BFDAEE78E0F2784C: R2356.1, R2374.1
XA524F62F8426DC6C6DDF: D2305.3 (COM), R2385.2, U2313.12 (+)
XABD60A45AAAC75EB8951: R2321.2, R2322.1
XAE848145CA35E48D128D: D2307.3 (COM), R2396.2, U2315.3 (+)
XAF8F046B41DDE12F9296: D2316.1 (K), D2324.2 (A), RV2313.2 (Wiper), RV2313.3 (CW), U2307.5, U2315.13 (-)
XAF706C326AEAB06E6E57: D2318.2 (A), D2319.1 (K)
XB2C49404EED0D6211270: Q2301.5 (B2), R2351.2
XB3F21E15F2E57CAF018B: D2313.1 (K), D2314.2 (A)
XB7ED59B1CB61B4742F41: R2374.2, R2375.1, U2307.13 (-)
XB9F035FC2AF2925E1E25: R2345.2, R2346.2, R2347.2, R2348.2, U2312.6 (-)
XB2372D5B4FBA41C24EE4: C2315.1, RB2301.1, U2315.8
XB2476C897A43616D2B8F: R2372.1, RV2311.2 (Wiper)
XB7440300A36C4430B968: D2317.2 (A), D2318.1 (K)
XBACFAB119A723846F935: R2390.2, U2307.1
XBC2CF0337E9CFDADBBCA: R2358.2, R2359.2, R2360.2, R2361.2, U2312.9 (-)
XBF3BE4FDE28392550991: R2359.1, U2313.1, U2313.2 (-)
XC6E99B62767290FBD2F8: R2370.2, R2371.1, U2307.3 (+)
XC12A5C4EF4E6A6244DC2: R2349.2, RV2307.2 (Wiper), RV2307.3 (CW), U2308.13 (-)
XC96CCF4BED0CAA479616: D2306.2 (A), Q2305.1 (B), R2389.2
XC830CABE5D3B659DB698: R2383.2, R2384.2, U2313.9 (-)
XCABBBE727D0B4D09C614: Q2302.1 (B), Q2302.3 (C), Q2303.1 (B), Q2304.1 (B), R2353.1
XCAFA40AF9494E073CDBA: R2302.1, R2347.1, RV2309.1 (CCW), RV2310.1 (CCW), RV2311.1 (CCW), RV2312.1 (CCW), U2308.7
XCD522340A42F2F46BD02: Q2301.1 (E1), Q2301.4 (E2), U2309.1
XCF7B60823204C84A5FA7: R2380.1, U2311.6 (-), U2311.7
XCFFAB9B2901CC053DFE1: C2302.1, U2301.6 (Vout), U2308.3 (+)
XD0A5E292A125A1D0DEC4: R2301.2, R2302.2, U2308.6 (-)
XD7D3FD891A5F9F9A6BC0: D2319.2 (A), D2320.1 (K)
XD9FC48F3F9F8150432DE: Q2301.6 (C1), RV2308.2 (Wiper), RV2308.3 (CW), U2309.2 (-)
XD12FF65395347EC7D1C0: R2323.2, R2324.1, U2310.5 (+)
XDBA54D73B417B8BBCDAE: R2354.2, U2306.1
XDC46BFCF608CE924783A: C2304.1, R2326.1, R2346.1, U2310.7
XDEC65E1C2FBB68F45A66: R2337.2, R2338.1
XDEDA32D515C912ED69C7: C2312.1, U2306.5, U2312.12 (+)
XE7AC1551C550B0461EBE: Q2306.3 (C), RB2302.1
XE498F205667E31536CD5: R2398.1, U2315.7, U2315.10 (+)
XE15497AEEB69BDAA0843: D2305.2 (K), D2307.2 (K), R2301.1, R2303.1, R2352.1, R2378.1, R2388.1, R2399.1, RV2309.3 (CW), RV2310.3 (CW), RV2311.3 (CW), RV2312.3 (CW), U2308.1, U2308.2 (-)
XEB38D85612513E2B4A8F: R2323.1
XEC5B997EA3C1C95F52E3: U2316.8, U2316.9 (-)
XEC485257BD01B056F78C: C2303.1, R2321.1, U2310.1
XF3BFDFD1C1C00AB7A4A7: R2384.1, R2385.1, U2313.8
XF4DFB1CF0D40F97932C2: Q2303.3 (C), R2354.1
XF5C940639BF958F9B92F: R2364.1, RV2309.2 (Wiper)
XF7AC2F2043D0D03218B9: D2314.1 (K), D2315.2 (A)
XF9CB226286EC6F21C449: R2387.1, U2314.1, U2314.5 (+)
XFA9179FF4E8D01632C80: R2341.1, U2311.10 (+)
XFACEAC4AD4236AE2EDC7: R2331.1
XFCB324788F68CEDB4559: D2320.2 (A), D2321.1 (K)
