Takazudo/zudo-osc-hole-field/boards/osc-core/sheets/mix4_vca_M4A_K.kicad_sch

## KiCad design boards/osc-core/sheets/mix4_vca_M4A_K.kicad_sch (2026-10-05)

Schematic: mix4_vca_M4A_K.kicad_sch

Parts:
C8301: 1e-07 F; C0603; MPN GRM188R71H104KA93D
C8302: 1e-06 F; C0603
C8303, C8305, C8307, C8309, C8311: 1e-10 F; C0603; MPN C0603C101J5GACTU
C8304, C8306, C8308, C8310, C8312: 1e-11 F; C0603
C8313: 1e-08 F; C0603
C8314: 100 pF; C0603; MPN C0603C101J5GACTU
C8315, C8326, C8327, C8332, C8333, C8334, C8335, C8336, C8337, C8338, C8339, C8340, C8341, C8342, C8343: 100 nF; C0603; MPN GRM188R71H104KA93D
D8313: BAT54S,215; SOT-23; MPN BAT54S,215
D8314: BAS16GW-QX; SOD-123; MPN BAS16GW-QX
Q8301: MMBT3906,215; SOT-23; MPN MMBT3906,215
R8301, R8302, R8310, R8320, R8330, R8340, R8355: 10000 Ω; R0603
R8303: 22000 Ω; R0603
R8304, R8313, R8314, R8323, R8324, R8333, R8334, R8343, R8344, R8358, R8359: 100000 Ω; R0603; MPN RT0603BRD07100KL
R8309, R8319, R8329, R8339, R8354, R8376: 100 Ω; R0603
R8311, R8321, R8331, R8341, R8356, R8360: 1000 Ω; R0603
R8312, R8322, R8332, R8342, R8357, R8361: 1e+07 Ω; R0603
R8345, R8346, R8347, R8348, R8362, R8363, R8364, R8365, R8366, R8368, R8369, R8370, R8371, R8375, R8379, R8380: 100 kΩ; R0603; MPN RT0603BRD07100KL
R8349: 50 kΩ; R0603
R8367, R8372, R8373, R8374: 10 kΩ; R0603
R8377: 1 MΩ; R0603
R8378: 1 kΩ; R0603
RV8307, RV8308: 10 kΩ; Potentiometer_Bourns_TC33X_Vertical; MPN TC33X-2-103E
U8301: REF5050AIDR; SOIC-8_3.9x4.9mm_P1.27mm; MPN REF5050AIDR; LCSC C27804
U8307: LM13700M/NOPB; SOIC-16_3.9x9.9mm_P1.27mm; MPN LM13700M/NOPB; LCSC C1346265
U8308: OPA4197IPWR; TSSOP-14_4.4x5mm_P0.65mm; MPN OPA4197IPWR; LCSC C2057327
U8309, U8310, U8311, U8312, U8313: OPA4196IDR; SOIC-14_3.9x8.7mm_P1.27mm; MPN OPA4196IDR; LCSC C2057385

Connections:
+12V: C8301.1, C8315.1, C8326.1, C8332.1, C8334.1, C8336.1, C8338.1, C8340.1, C8342.1, U8301.2 (Vin), U8307.11 (V+), U8308.4 (V+), U8309.4 (V+), U8310.4 (V+), U8311.4 (V+), U8312.4 (V+), U8313.4 (V+)
-12V: C8327.1, C8333.1, C8335.1, C8337.1, C8339.1, C8341.1, C8343.1, R8379.2, U8307.6 (V-), U8308.11 (V-), U8309.11 (V-), U8310.11 (V-), U8311.11 (V-), U8312.11 (V-), U8313.11 (V-)
AGND: C8301.2, C8302.2, C8313.2, C8315.2, C8326.2, C8327.2, C8332.2, C8333.2, C8334.2, C8335.2, C8336.2, C8337.2, C8338.2, C8339.2, C8340.2, C8341.2, C8342.2, C8343.2, D8313.1 (A), R8304.2, R8312.2, R8322.2, R8332.2, R8342.2, R8357.2, R8361.2, R8369.2, R8376.2, R8378.2, U8301.4 (GND), U8307.7, U8307.10, U8307.13 (-), U8307.14 (+), U8308.5 (+), U8308.12 (+), U8311.3 (+), U8312.3 (+), U8312.5 (+), U8313.5 (+), U8313.10 (+), U8313.12 (+)
X0A9E3D496EABD333AB39: C8312.1, R8359.1, R8363.1, U8311.8
X0BD2CDFE2274B273C261: C8314.2, D8314.1 (K), Q8301.2 (E), R8372.2, U8313.2 (-)
X0D060943AD17FE38FCB2: C8312.2, R8358.2, R8359.2, U8311.9 (-)
X1B47ACA4ED467820F473: R8311.2, R8312.1, U8309.5 (+)
X1BABC889D5DC46375BC9: R8303.2, R8304.1, U8308.10 (+)
X1FFDC49339C7C2982F1A: R8321.1
X3A08019A7B3A44284122: C8303.2, R8310.2, U8309.2 (-)
X3AB54520A2932F40FFB8: RV8308.2 (Wiper), RV8308.3 (CW), U8307.5, U8313.6 (-)
X3C092ED557D16F7678FC: R8313.1, U8309.3 (+)
X3DC759138DE26EC48593: R8323.1, U8309.10 (+)
X3FBD8C759E6C6B90C8E9: C8306.2, R8323.2, R8324.2, U8309.13 (-)
X4B30B1EF4D9C14E004A0: C8313.1, R8360.2, R8361.1, U8311.12 (+)
X6A0990702B5163F99131: R8349.1, R8375.1, U8311.1
X7A98BCC092BC8A3D8623: C8305.1, R8319.1, U8309.8
X7B5C74E08F15CF029DD6: D8313.2 (K), R8301.1, R8303.1, R8368.1, R8372.1, RV8307.3 (CW), U8308.1, U8308.2 (-)
X7B545BC6CA49A1F0FF11: R8358.1, U8311.5 (+)
X7DF663BE2423DFFBEEC1: C8310.2, R8343.2, R8344.2, U8310.13 (-)
X7FF97B97D3E1211D55D1: R8331.2, R8332.1, U8310.5 (+)
X8F1B578D3860FDE9AA50: R8380.2, RV8308.1 (CCW)
X9DE32D9DB5A523EC960E: C8310.1, R8344.1, R8348.1, U8310.14
X28C67DFB80DE00C4D66C: R8374.2, U8307.1
X33CA5B7F1AD1677C7737: R8331.1
X57F1DE8C7AC7967AEEDE: D8314.2 (A), Q8301.1 (B), R8373.2
X59D73A1F5293EAD9165B: R8362.2, R8363.2, R8364.2, U8312.2 (-)
X76CBC2A15ACB37487709: R8341.1
X80DE516FDAD10BCAF6C3: U8313.8, U8313.9 (-)
X91AB2074CD577F2FF2D8: R8329.2, R8330.1
X315F936FAE31EB7DE1C9: R8375.2, R8376.1, U8307.3 (+)
X489F21AF98C74FBB046F: R8356.1
X599C0521F9B755123DA7: C8311.1, R8354.1, U8311.7
X665F99D69A5D3F2A216F: R8319.2, R8320.1
X746B462C6A316142F2A3: C8308.1, R8334.1, R8347.1, U8310.7
X1917C2DF31998D75E05B: R8341.2, R8342.1, U8310.12 (+)
X3074F183533AED0A29EB: R8370.2, R8371.2, U8312.13 (-)
X38743C4DC0B3136738CF: C8303.1, R8309.1, U8309.1
X53912B1E6E7E640E4157: R8343.1, U8310.10 (+)
X58381FC52FCDDA9B0131: R8339.2, R8340.1
X80540E99F27AA7B71015: R8366.1, R8367.1, U8312.7
X296064ECC2BFFEBAF21B: R8368.2, R8369.1, U8312.12 (+)
X984244CB12A6C5A72197: R8377.2, R8378.1, U8307.4 (-)
X2620246FAC3FF931C427: R8354.2, R8355.1
X16403069BAF66D8DF61B: C8304.2, R8313.2, R8314.2, U8309.6 (-)
X22673737DADEA6D168CE: C8304.1, R8314.1, R8345.1, U8309.7
XA16BE2D8C2D07015E3FC: R8309.2, R8310.1
XA26881997A20C7F47345: R8301.2, R8302.2, U8308.6 (-)
XACB4939E4CA4AAFF80B0: R8302.1, RV8307.1 (CCW), U8308.7
XAF99EB621CFEA4931C6B: C8302.1, U8301.6 (Vout), U8308.3 (+)
XB02B9EB9C6E6BEAF55C0: C8308.2, R8333.2, R8334.2, U8310.6 (-)
XBF5A9858FD7F082342D0: Q8301.3 (C), R8374.1
XC8AA06D3B926ED6C1B00: R8380.1, U8313.7
XC30F92F6FBBC81D43F88: R8321.2, R8322.1, U8309.12 (+)
XC36B571E611AA7A9BD4F: R8371.1, U8312.14, U8313.3 (+)
XCDCA9BC2ED0E8F397677: U8308.8, U8308.9 (-)
XCF03A7F92F68C1D90B0B: R8362.1, U8311.13 (-), U8311.14
XCFFE7511BC889FE8CD18: R8311.1
XD0ECE5D89DD5E2B4ADAC: U8313.13 (-), U8313.14
XD61AA59B6F4656314313: R8333.1, U8310.3 (+)
XD228CF4C509DD84C8B2D: R8364.1, R8365.1, U8312.1
XDADFE7B0C73DF5FDCA7F: C8311.2, R8355.2, U8311.6 (-)
XDAF106542F728D33D984: C8307.2, R8330.2, U8310.2 (-)
XDB86D54026FA0D3F6BC2: R8370.1, U8312.8, U8312.9 (-)
XDDCE065E98500A899CAC: U8308.13 (-), U8308.14
XDF85AE003026630AB996: R8377.1, RV8307.2 (Wiper)
XE70CD3179D3A13387B23: R8360.1
XE798B65C0571C5DD4937: D8313.3 (COM), R8367.2, U8312.10 (+)
XEC2F160CA08EE3949036: R8365.2, R8366.2, U8312.6 (-)
XEE654ADFB565DFEACABD: R8345.2, R8346.2, R8347.2, R8348.2, R8349.2, U8311.2 (-)
XEF116045831B5DDCF09F: C8309.1, R8339.1, U8310.8
XF2C5B81033E0E3AB7394: C8305.2, R8320.2, U8309.9 (-)
XF8C4861664885936F616: C8306.1, R8324.1, R8346.1, U8309.14
XF08EB34AF5EDC24D734B: R8356.2, R8357.1, U8311.10 (+)
XF66A5144E466D78AAD0C: C8307.1, R8329.1, U8310.1
XF67A44940AEC7D3E43D4: R8379.1, U8307.16
XF337836BEE991B4CBBB4: C8314.1, R8373.1, U8313.1
XFE0B9FCF3ECBF3D36FF4: C8309.2, R8340.2, U8310.9 (-)
