Takazudo/zudo-osc-hole-field/boards/osc-core/sheets/mix4_vca_M4B_K.kicad_sch

## KiCad design boards/osc-core/sheets/mix4_vca_M4B_K.kicad_sch (2026-10-05)

Schematic: mix4_vca_M4B_K.kicad_sch

Parts:
C8401: 1e-07 F; C0603; MPN GRM188R71H104KA93D
C8402: 1e-06 F; C0603
C8403, C8405, C8407, C8409, C8411: 1e-10 F; C0603; MPN C0603C101J5GACTU
C8404, C8406, C8408, C8410, C8412: 1e-11 F; C0603
C8413: 1e-08 F; C0603
C8414: 100 pF; C0603; MPN C0603C101J5GACTU
C8415, C8426, C8427, C8432, C8433, C8434, C8435, C8436, C8437, C8438, C8439, C8440, C8441, C8442, C8443: 100 nF; C0603; MPN GRM188R71H104KA93D
D8413: BAT54S,215; SOT-23; MPN BAT54S,215
D8414: BAS16GW-QX; SOD-123; MPN BAS16GW-QX
Q8401: MMBT3906,215; SOT-23; MPN MMBT3906,215
R8401, R8402, R8410, R8420, R8430, R8440, R8455: 10000 Ω; R0603
R8403: 22000 Ω; R0603
R8404, R8413, R8414, R8423, R8424, R8433, R8434, R8443, R8444, R8458, R8459: 100000 Ω; R0603; MPN RT0603BRD07100KL
R8409, R8419, R8429, R8439, R8454, R8476: 100 Ω; R0603
R8411, R8421, R8431, R8441, R8456, R8460: 1000 Ω; R0603
R8412, R8422, R8432, R8442, R8457, R8461: 1e+07 Ω; R0603
R8445, R8446, R8447, R8448, R8462, R8463, R8464, R8465, R8466, R8468, R8469, R8470, R8471, R8475, R8479, R8480: 100 kΩ; R0603; MPN RT0603BRD07100KL
R8449: 50 kΩ; R0603
R8467, R8472, R8473, R8474: 10 kΩ; R0603
R8477: 1 MΩ; R0603
R8478: 1 kΩ; R0603
RV8407, RV8408: 10 kΩ; Potentiometer_Bourns_TC33X_Vertical; MPN TC33X-2-103E
U8401: REF5050AIDR; SOIC-8_3.9x4.9mm_P1.27mm; MPN REF5050AIDR; LCSC C27804
U8407: LM13700M/NOPB; SOIC-16_3.9x9.9mm_P1.27mm; MPN LM13700M/NOPB; LCSC C1346265
U8408: OPA4197IPWR; TSSOP-14_4.4x5mm_P0.65mm; MPN OPA4197IPWR; LCSC C2057327
U8409, U8410, U8411, U8412, U8413: OPA4196IDR; SOIC-14_3.9x8.7mm_P1.27mm; MPN OPA4196IDR; LCSC C2057385

Connections:
+12V: C8401.1, C8415.1, C8426.1, C8432.1, C8434.1, C8436.1, C8438.1, C8440.1, C8442.1, U8401.2 (Vin), U8407.11 (V+), U8408.4 (V+), U8409.4 (V+), U8410.4 (V+), U8411.4 (V+), U8412.4 (V+), U8413.4 (V+)
-12V: C8427.1, C8433.1, C8435.1, C8437.1, C8439.1, C8441.1, C8443.1, R8479.2, U8407.6 (V-), U8408.11 (V-), U8409.11 (V-), U8410.11 (V-), U8411.11 (V-), U8412.11 (V-), U8413.11 (V-)
AGND: C8401.2, C8402.2, C8413.2, C8415.2, C8426.2, C8427.2, C8432.2, C8433.2, C8434.2, C8435.2, C8436.2, C8437.2, C8438.2, C8439.2, C8440.2, C8441.2, C8442.2, C8443.2, D8413.1 (A), R8404.2, R8412.2, R8422.2, R8432.2, R8442.2, R8457.2, R8461.2, R8469.2, R8476.2, R8478.2, U8401.4 (GND), U8407.7, U8407.10, U8407.13 (-), U8407.14 (+), U8408.5 (+), U8408.12 (+), U8411.3 (+), U8412.3 (+), U8412.5 (+), U8413.5 (+), U8413.10 (+), U8413.12 (+)
X0F0A9453B7270BE7EDD0: D8413.3 (COM), R8467.2, U8412.10 (+)
X01AB747CAB1FBE80C06A: R8421.2, R8422.1, U8409.12 (+)
X2ADF75CC254020C84459: C8414.2, D8414.1 (K), Q8401.2 (E), R8472.2, U8413.2 (-)
X2BA1EDE6C92351885A00: C8406.1, R8424.1, R8446.1, U8409.14
X3DAC76D7A558264A3F1B: R8439.2, R8440.1
X4A88CCE54DCC5E6D618C: C8410.2, R8443.2, R8444.2, U8410.13 (-)
X4AD789F56C4006DE7DA9: R8460.1
X5ADCADC7FACEC0D733A5: C8407.2, R8430.2, U8410.2 (-)
X5E8077D32AE688EB2B25: C8403.2, R8410.2, U8409.2 (-)
X6A41CB366F009D32C578: R8413.1, U8409.3 (+)
X7A887447F4726336445D: C8410.1, R8444.1, R8448.1, U8410.14
X7B5491F9A79EA68E9ED1: R8475.2, R8476.1, U8407.3 (+)
X7DF11C74936D4F35CC1C: R8443.1, U8410.10 (+)
X7EEE222FB78D795E1039: R8480.2, RV8408.1 (CCW)
X7F13D0F108F8B02BD4BC: C8404.2, R8413.2, R8414.2, U8409.6 (-)
X8C5AC7F086620BD395BC: R8477.1, RV8407.2 (Wiper)
X010BBC55D32CBEB7B85A: C8404.1, R8414.1, R8445.1, U8409.7
X55AD269F9DBA0DA80E15: C8408.2, R8433.2, R8434.2, U8410.6 (-)
X064CAFC6EF9ED70E814C: R8423.1, U8409.10 (+)
X65F25611171FAF04B868: R8445.2, R8446.2, R8447.2, R8448.2, R8449.2, U8411.2 (-)
X71E430E637630D0C176D: C8407.1, R8429.1, U8410.1
X78BCBEEA970FF3146D79: C8412.2, R8458.2, R8459.2, U8411.9 (-)
X95CA525C4F8BCA8B4A13: R8465.2, R8466.2, U8412.6 (-)
X159FBF6DE77D7E9413DA: C8408.1, R8434.1, R8447.1, U8410.7
X256D7A2CAD19377722D0: R8401.2, R8402.2, U8408.6 (-)
X399F6DD667FA12CDEFF6: U8408.13 (-), U8408.14
X501E2D1E4257965998BA: D8414.2 (A), Q8401.1 (B), R8473.2
X562DE86396A7D47EC7FC: R8411.2, R8412.1, U8409.5 (+)
X950CCD6FCC5D64193E82: R8466.1, R8467.1, U8412.7
X2235AA409133311006A2: D8413.2 (K), R8401.1, R8403.1, R8468.1, R8472.1, RV8407.3 (CW), U8408.1, U8408.2 (-)
X3878A543A34D0072B9DD: R8429.2, R8430.1
X4175BB0C7CB01381A62A: C8411.2, R8455.2, U8411.6 (-)
X38972CC7F44C1668286B: R8462.2, R8463.2, R8464.2, U8412.2 (-)
X46270C135ACB2EB383FC: R8421.1
X92486F8175BA405F603C: C8414.1, R8473.1, U8413.1
X347406F0EA51437997A0: C8402.1, U8401.6 (Vout), U8408.3 (+)
X826169EDE09D7A95D8A3: R8454.2, R8455.1
X9476738BD551C8789386: R8449.1, R8475.1, U8411.1
X93401982C2F89B584227: R8431.1
X359635686D1CF172FEC3: R8431.2, R8432.1, U8410.5 (+)
X6825025214AA633E7D74: R8468.2, R8469.1, U8412.12 (+)
X529019320568CBE0C17F: R8474.2, U8407.1
X10151698937763D36E0E: R8470.2, R8471.2, U8412.13 (-)
XA298250074404F530DD4: R8441.1
XAD2A38741611D509A34E: R8419.2, R8420.1
XAF0006BBB47903BAAB0C: C8411.1, R8454.1, U8411.7
XB3C59E1A9CFF93C9C7D7: R8456.2, R8457.1, U8411.10 (+)
XB08FE271FD1E7E3F3792: R8409.2, R8410.1
XB9F7C7FAA057C204FF64: R8402.1, RV8407.1 (CCW), U8408.7
XB482D9FE97C1715C6898: C8409.2, R8440.2, U8410.9 (-)
XB337748746F5F263A478: R8441.2, R8442.1, U8410.12 (+)
XBC0F532AC8D75312C130: C8405.2, R8420.2, U8409.9 (-)
XCC2FBAA1AD49E9E30B09: U8408.8, U8408.9 (-)
XCC47A52E5359EC16D22A: R8477.2, R8478.1, U8407.4 (-)
XCD9F9C408F5CCC3A8E61: C8412.1, R8459.1, R8463.1, U8411.8
XD0AB63C429782D345CFA: R8411.1
XD2E8324144E33A4C4C67: R8403.2, R8404.1, U8408.10 (+)
XD7829BF2DA4B1DFD9DC4: C8409.1, R8439.1, U8410.8
XD2798469F19CC228BD93: U8413.8, U8413.9 (-)
XDFBA55F8B540FE101CD8: R8433.1, U8410.3 (+)
XE7A8EB7600574A69E6E9: C8406.2, R8423.2, R8424.2, U8409.13 (-)
XE31A80290D2BC578861C: R8458.1, U8411.5 (+)
XE71F9B1073D3C5A3C006: RV8408.2 (Wiper), RV8408.3 (CW), U8407.5, U8413.6 (-)
XE250C97BB57EAC0B774F: R8470.1, U8412.8, U8412.9 (-)
XE614CDD1E4D4F5E04240: C8413.1, R8460.2, R8461.1, U8411.12 (+)
XE890E75323C46A881F82: Q8401.3 (C), R8474.1
XF3CCAC222AC18F4DEE59: R8471.1, U8412.14, U8413.3 (+)
XF5B336FA58FAE627348E: R8464.1, R8465.1, U8412.1
XF9B1E336250748F21943: C8403.1, R8409.1, U8409.1
XF42CEF50187A4B848801: C8405.1, R8419.1, U8409.8
XF64CE2464C26725B93EA: R8456.1
XF12351C36A39088567FF: R8480.1, U8413.7
XFA118926C302A3F5455A: R8479.1, U8407.16
XFC2CD956969D8B0C8140: U8413.13 (-), U8413.14
XFC5797B95973FE8AA868: R8462.1, U8411.13 (-), U8411.14
