Takazudo/zudo-osc-hole-field/boards/osc-core/sheets/mix5_M5A_K.kicad_sch

## KiCad design boards/osc-core/sheets/mix5_M5A_K.kicad_sch (2026-10-05)

Schematic: mix5_M5A_K.kicad_sch

Parts:
C8101: 1e-07 F; C0603; MPN GRM188R71H104KA93D
C8102: 1e-06 F; C0603
C8103, C8105, C8107, C8109, C8111, C8113: 1e-10 F; C0603; MPN C0603C101J5GACTU
C8104, C8106, C8108, C8110, C8112: 1e-11 F; C0603
C8114, C8129, C8130, C8131, C8132, C8133, C8134, C8135, C8136, C8137, C8138: 100 nF; C0603; MPN GRM188R71H104KA93D
R8101, R8102, R8110, R8120, R8130, R8140, R8150, R8162: 10000 Ω; R0603
R8103: 22000 Ω; R0603
R8104, R8113, R8114, R8123, R8124, R8133, R8134, R8143, R8144, R8153, R8154: 100000 Ω; R0603; MPN RT0603BRD07100KL
R8109, R8119, R8129, R8139, R8149, R8161: 100 Ω; R0603
R8111, R8121, R8131, R8141, R8151, R8163: 1000 Ω; R0603
R8112, R8122, R8132, R8142, R8152, R8164: 1e+07 Ω; R0603
R8155, R8156, R8157, R8158, R8159, R8165, R8166: 100 kΩ; R0603; MPN RT0603BRD07100KL
R8160: 40 kΩ; R0603
U8101: REF5050AIDR; SOIC-8_3.9x4.9mm_P1.27mm; MPN REF5050AIDR; LCSC C27804
U8107: OPA4197IPWR; TSSOP-14_4.4x5mm_P0.65mm; MPN OPA4197IPWR; LCSC C2057327
U8108, U8109, U8110, U8111: OPA4196IDR; SOIC-14_3.9x8.7mm_P1.27mm; MPN OPA4196IDR; LCSC C2057385

Connections:
+12V: C8101.1, C8114.1, C8129.1, C8131.1, C8133.1, C8135.1, C8137.1, U8101.2 (Vin), U8107.4 (V+), U8108.4 (V+), U8109.4 (V+), U8110.4 (V+), U8111.4 (V+)
-12V: C8130.1, C8132.1, C8134.1, C8136.1, C8138.1, U8107.11 (V-), U8108.11 (V-), U8109.11 (V-), U8110.11 (V-), U8111.11 (V-)
AGND: C8101.2, C8102.2, C8114.2, C8129.2, C8130.2, C8131.2, C8132.2, C8133.2, C8134.2, C8135.2, C8136.2, C8137.2, C8138.2, R8104.2, R8112.2, R8122.2, R8132.2, R8142.2, R8152.2, R8164.2, U8101.4 (GND), U8107.5 (+), U8107.12 (+), U8110.10 (+), U8111.5 (+), U8111.10 (+), U8111.12 (+)
X0A6A96AB2257B55BC685: C8103.2, R8110.2, U8108.2 (-)
X1BB107FFA26A5327B18E: R8165.1, U8111.1, U8111.2 (-)
X2F0FD4B4311AA5F20EBD: R8155.2, R8156.2, R8157.2, R8158.2, R8159.2, R8160.2, U8110.9 (-)
X3F9931ACD1A8A527BDB6: R8163.1
X6BD40278C60E8AC692D2: C8112.1, R8154.1, R8159.1, U8110.7
X7DC561B7FAF374EE5AB0: R8113.1, U8108.3 (+)
X7F5FECDFC17CC6784223: C8108.2, R8133.2, R8134.2, U8109.6 (-)
X8FFBDC9C42EC02C29B2F: R8121.1
X9A2A689D1C741BE6AFED: R8141.1
X9E3B644052FEA549648A: R8163.2, R8164.1, U8111.3 (+)
X27C28FDCAA9450E228E6: R8129.2, R8130.1
X31B7F6457D5A23DBA19E: C8112.2, R8153.2, R8154.2, U8110.6 (-)
X51F6671C66B653F81BC5: C8104.1, R8114.1, R8155.1, U8108.7
X54B887442598D18F9FD9: C8104.2, R8113.2, R8114.2, U8108.6 (-)
X72E25DC791B1E8D9A74C: C8106.2, R8123.2, R8124.2, U8108.13 (-)
X78C1702B66BDCEBC593E: R8131.1
X82C1C13F85BFB08DFB5F: C8105.1, R8119.1, U8108.8
X90A3CD82F6E195F644DD: R8153.1, U8110.3 (+)
X264AFDA30C804B1B03D4: C8103.1, R8109.1, U8108.1
X0267D452297082CBFD6A: R8101.2, R8102.2, U8107.6 (-)
X272ADBD100FF77E2EEEE: R8123.1, U8108.10 (+)
X555CDD0061680F23773B: C8108.1, R8134.1, R8157.1, U8109.7
X567D5C752D604876B08A: R8111.1
X0615A446E46FA664032B: R8143.1, U8109.10 (+)
X745F3B5FCA8C34C840D3: R8111.2, R8112.1, U8108.5 (+)
X751F9510BCFE681FFFE0: U8107.13 (-), U8107.14
X895BBF67BE56E503D0AA: C8111.2, R8150.2, U8110.2 (-)
X910F540EE06F9EEA2414: C8102.1, U8101.6 (Vout), U8107.3 (+)
X3245E446D0AC7D6BACBF: R8102.1, U8107.7
X8513A9265CE9B8AA4E49: R8160.1, U8110.8, U8110.12 (+)
X50214D29D17C9AFAE6DD: C8106.1, R8124.1, R8156.1, U8108.14
X85155FD08479E37DFE6A: R8151.2, R8152.1, U8110.5 (+)
X95411E05A42CBD2FD0AE: C8111.1, R8149.1, U8110.1
X14911084ED0BF0C86F85: C8113.1, R8161.1, U8110.14
X20138693CA14267952D1: C8109.1, R8139.1, U8109.8
XA30BB00DD486B18599B6: U8111.8, U8111.9 (-)
XA1376930C555476901BB: R8166.1, U8111.7
XA3746668ABD6A5DFF19C: C8107.2, R8130.2, U8109.2 (-)
XB4AD0134CD4F00FAFC83: C8113.2, R8162.2, U8110.13 (-)
XB5FB4914A1E34BDF7357: R8121.2, R8122.1, U8108.12 (+)
XB14B0A3E92D1F98FCAB4: R8165.2, R8166.2, U8111.6 (-)
XCB714A8ADD12C505EAFF: R8103.2, R8104.1, U8107.10 (+)
XD0AC980CC381CB2DED7A: R8151.1
XD0AEDF2201C438BC951F: R8161.2, R8162.1
XDD800F50FD90B14653CC: R8141.2, R8142.1, U8109.12 (+)
XDF1C8716B6AD108DEC54: U8107.8, U8107.9 (-)
XDF16E67D261B2F0A55CA: C8107.1, R8129.1, U8109.1
XDF62172BE5B25A600C9B: R8149.2, R8150.1
XDFE73EDB3AA45015AAD2: R8133.1, U8109.3 (+)
XEC4C271577BFE8DBACB5: R8101.1, R8103.1, U8107.1, U8107.2 (-)
XEF450FAFB7948719B206: R8131.2, R8132.1, U8109.5 (+)
XF1BB0E6D5FC2BB6E2776: C8105.2, R8120.2, U8108.9 (-)
XF7A09A49BFFF2E1410A0: R8139.2, R8140.1
XF56F4DA8E29974FB0CE5: C8110.1, R8144.1, R8158.1, U8109.14
XF98E7C4AE59913C0EB61: R8119.2, R8120.1
XF195CC86A82C6BA38868: R8109.2, R8110.1
XF246157287C665EF32A9: U8111.13 (-), U8111.14
XFFC240C39D4D5347BE27: C8110.2, R8143.2, R8144.2, U8109.13 (-)
XFFCE6A506588092A2930: C8109.2, R8140.2, U8109.9 (-)
