Takazudo/zudo-osc-hole-field/boards/osc-core/sheets/mix5_M5B_K.kicad_sch

## KiCad design boards/osc-core/sheets/mix5_M5B_K.kicad_sch (2026-10-05)

Schematic: mix5_M5B_K.kicad_sch

Parts:
C8201: 1e-07 F; C0603; MPN GRM188R71H104KA93D
C8202: 1e-06 F; C0603
C8203, C8205, C8207, C8209, C8211, C8213: 1e-10 F; C0603; MPN C0603C101J5GACTU
C8204, C8206, C8208, C8210, C8212: 1e-11 F; C0603
C8214, C8229, C8230, C8231, C8232, C8233, C8234, C8235, C8236, C8237, C8238: 100 nF; C0603; MPN GRM188R71H104KA93D
R8201, R8202, R8210, R8220, R8230, R8240, R8250, R8262: 10000 Ω; R0603
R8203: 22000 Ω; R0603
R8204, R8213, R8214, R8223, R8224, R8233, R8234, R8243, R8244, R8253, R8254: 100000 Ω; R0603; MPN RT0603BRD07100KL
R8209, R8219, R8229, R8239, R8249, R8261: 100 Ω; R0603
R8211, R8221, R8231, R8241, R8251, R8263: 1000 Ω; R0603
R8212, R8222, R8232, R8242, R8252, R8264: 1e+07 Ω; R0603
R8255, R8256, R8257, R8258, R8259, R8265, R8266: 100 kΩ; R0603; MPN RT0603BRD07100KL
R8260: 40 kΩ; R0603
U8201: REF5050AIDR; SOIC-8_3.9x4.9mm_P1.27mm; MPN REF5050AIDR; LCSC C27804
U8207: OPA4197IPWR; TSSOP-14_4.4x5mm_P0.65mm; MPN OPA4197IPWR; LCSC C2057327
U8208, U8209, U8210, U8211: OPA4196IDR; SOIC-14_3.9x8.7mm_P1.27mm; MPN OPA4196IDR; LCSC C2057385

Connections:
+12V: C8201.1, C8214.1, C8229.1, C8231.1, C8233.1, C8235.1, C8237.1, U8201.2 (Vin), U8207.4 (V+), U8208.4 (V+), U8209.4 (V+), U8210.4 (V+), U8211.4 (V+)
-12V: C8230.1, C8232.1, C8234.1, C8236.1, C8238.1, U8207.11 (V-), U8208.11 (V-), U8209.11 (V-), U8210.11 (V-), U8211.11 (V-)
AGND: C8201.2, C8202.2, C8214.2, C8229.2, C8230.2, C8231.2, C8232.2, C8233.2, C8234.2, C8235.2, C8236.2, C8237.2, C8238.2, R8204.2, R8212.2, R8222.2, R8232.2, R8242.2, R8252.2, R8264.2, U8201.4 (GND), U8207.5 (+), U8207.12 (+), U8210.10 (+), U8211.5 (+), U8211.10 (+), U8211.12 (+)
X0B98D1C9C566C4D41558: C8209.2, R8240.2, U8209.9 (-)
X1D5083C1689CCBDCC7AF: R8233.1, U8209.3 (+)
X2A2A5507221877F5CADE: C8207.2, R8230.2, U8209.2 (-)
X4E9DA5171986B7A73694: R8241.1
X5CBF72FAD010793D6DA4: R8263.2, R8264.1, U8211.3 (+)
X5CD5EA02032391EA4821: R8253.1, U8210.3 (+)
X5D8D68279137D15D762C: C8211.2, R8250.2, U8210.2 (-)
X7D55C76349110E6BFA30: C8205.2, R8220.2, U8208.9 (-)
X8DD8DBD8E9818361DFC9: C8213.2, R8262.2, U8210.13 (-)
X9DEA3D05C0252C14732B: R8260.1, U8210.8, U8210.12 (+)
X14E3C0C55CB1C4A95F24: R8249.2, R8250.1
X19B1E1FF84711BE7F475: R8202.1, U8207.7
X19DFE4ECB7BB9CFB3048: C8202.1, U8201.6 (Vout), U8207.3 (+)
X23BE1E15CB03226B28D1: U8207.8, U8207.9 (-)
X27B80377B6C412E86A02: R8263.1
X70AC166CEC330E51590C: R8251.2, R8252.1, U8210.5 (+)
X70DC76294A6404803334: R8209.2, R8210.1
X76D81676C30D329CC9B5: R8231.1
X80D227F98604B9CBA441: R8211.2, R8212.1, U8208.5 (+)
X95D8819DB1C3E612D316: C8208.2, R8233.2, R8234.2, U8209.6 (-)
X449B5773413913967757: R8241.2, R8242.1, U8209.12 (+)
X529FD52B2842B54F58F4: C8209.1, R8239.1, U8209.8
X557F548F7D9FAD9BFC62: R8213.1, U8208.3 (+)
X798C830883F5B46A491E: U8207.13 (-), U8207.14
X1350D6DDB5A475CC1BA8: R8201.1, R8203.1, U8207.1, U8207.2 (-)
X2270A6B4B24B2ED886CC: C8211.1, R8249.1, U8210.1
X6344EB8475DB1B237A5E: C8207.1, R8229.1, U8209.1
X07234E2FF52429093754: R8229.2, R8230.1
X30269F3CEEC0A946D838: R8201.2, R8202.2, U8207.6 (-)
X54369F0391B36FFB32D8: C8212.2, R8253.2, R8254.2, U8210.6 (-)
X649135E2E9A5ED5B0367: R8261.2, R8262.1
X3710249F479E7DA6DFCE: C8212.1, R8254.1, R8259.1, U8210.7
X9091883BB350F0D9A8E1: C8205.1, R8219.1, U8208.8
X745896914690CAAA678B: R8231.2, R8232.1, U8209.5 (+)
XA1B998C0DDF30A5D6552: R8203.2, R8204.1, U8207.10 (+)
XA585181D0B9DE3587445: R8251.1
XB4B9449C2C9EB5819317: U8211.13 (-), U8211.14
XB9C83C62FAFA64A9376E: R8223.1, U8208.10 (+)
XB9D8E425159DDB4164F8: C8206.1, R8224.1, R8256.1, U8208.14
XB77A49BB412844B458C3: R8239.2, R8240.1
XB8780C34DCDC50D9A9BA: R8266.1, U8211.7
XBD016377D3E11EE7414C: R8265.1, U8211.1, U8211.2 (-)
XBEC77FAFF5C8CCFC310A: R8255.2, R8256.2, R8257.2, R8258.2, R8259.2, R8260.2, U8210.9 (-)
XC4E5128215CBF5650706: C8210.2, R8243.2, R8244.2, U8209.13 (-)
XC8F08969780264FD50DA: C8208.1, R8234.1, R8257.1, U8209.7
XD02CA67ED16EE756D426: C8204.2, R8213.2, R8214.2, U8208.6 (-)
XD9E610B68315B208DD4E: C8210.1, R8244.1, R8258.1, U8209.14
XD35CC6F950919CDBDA22: R8219.2, R8220.1
XD6462BCAEA6B5594D150: U8211.8, U8211.9 (-)
XDC7C2141748820FC9667: C8206.2, R8223.2, R8224.2, U8208.13 (-)
XDC689FCDF5CBA0DA1EF3: R8211.1
XE6D6BCE3549DC12813C8: R8265.2, R8266.2, U8211.6 (-)
XEAF45AF487390AECB855: R8221.2, R8222.1, U8208.12 (+)
XEEFEC85AE93D9D9A8E3F: C8203.2, R8210.2, U8208.2 (-)
XF2C00B9C5BFB787A03DA: C8213.1, R8261.1, U8210.14
XF3BE3F5F807C19D144CA: C8204.1, R8214.1, R8255.1, U8208.7
XF73FE32FB15AF76B6C21: R8221.1
XF15093AA2AADB3B4C4FF: C8203.1, R8209.1, U8208.1
XFC9D33C023228B9841B7: R8243.1, U8209.10 (+)
