Takazudo/zudo-osc-hole-field/boards/osc-core/sheets/noise_N1_K.kicad_sch

## KiCad design boards/osc-core/sheets/noise_N1_K.kicad_sch (2026-10-05)

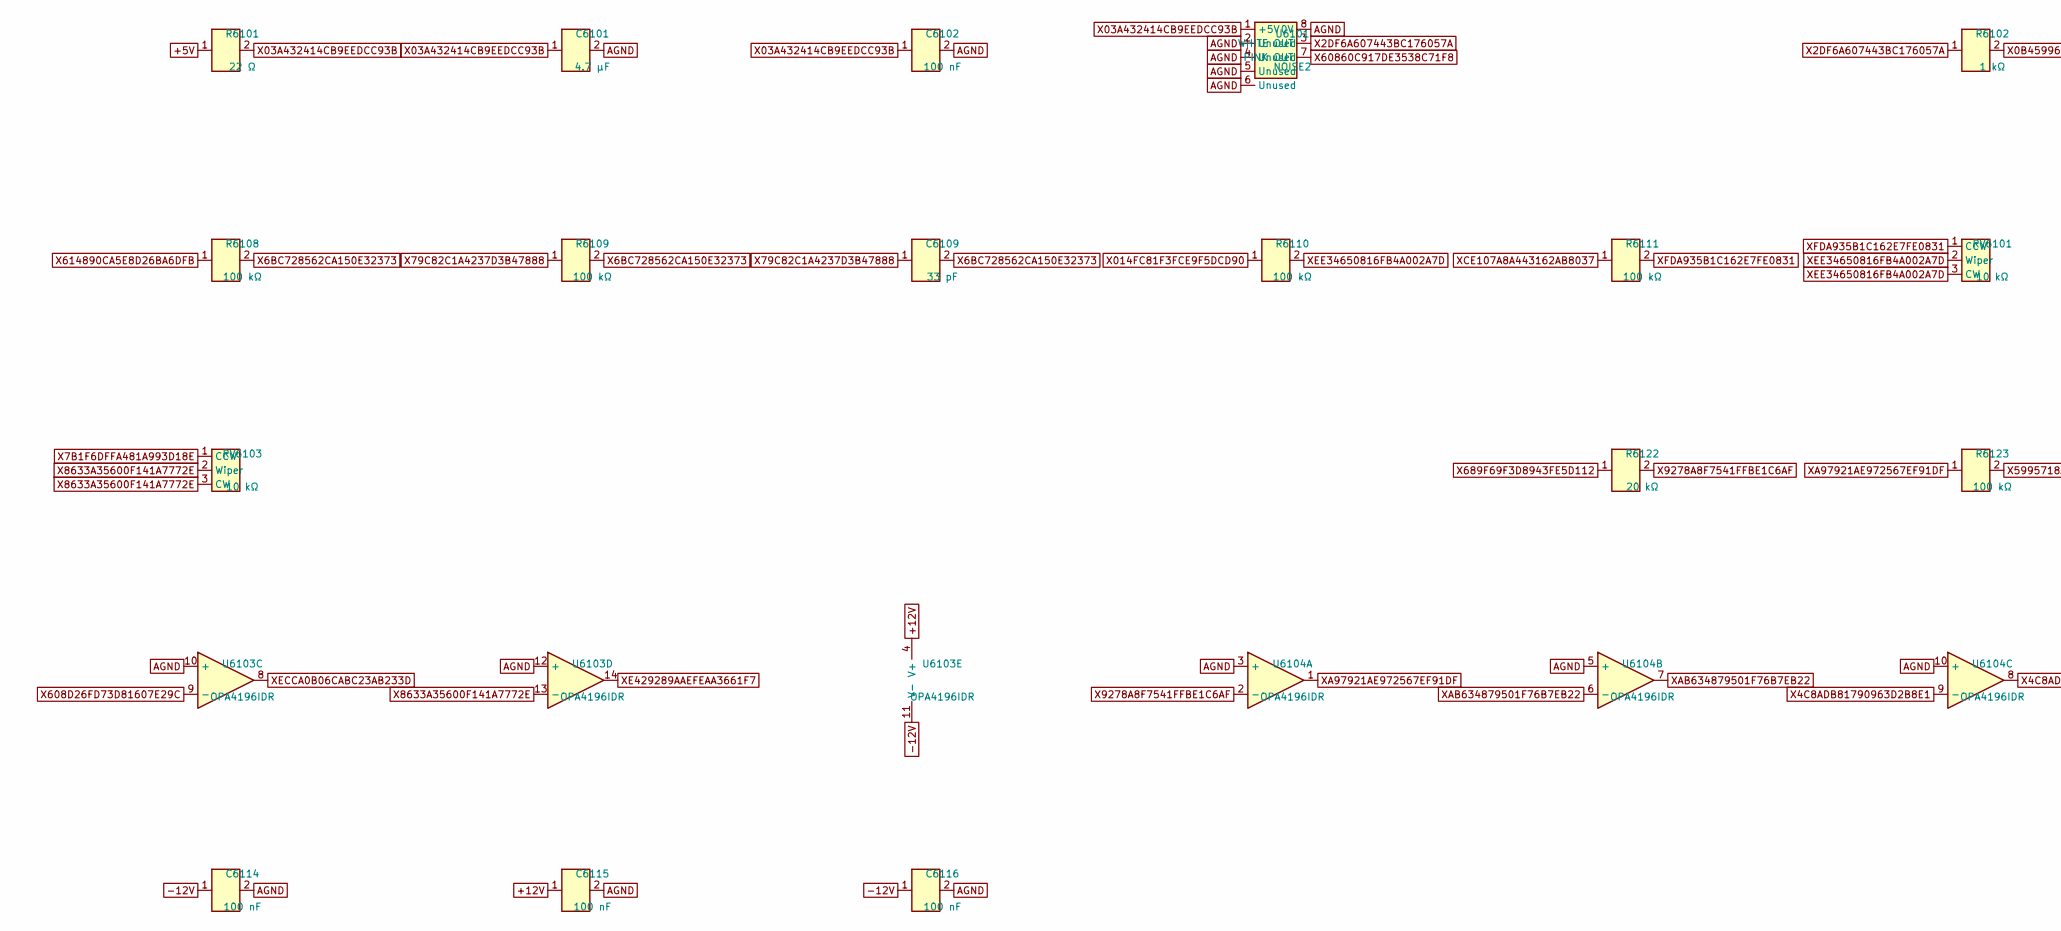
[picture p158: schematic noise_N1_K.kicad_sch, part in row 1, column 1]

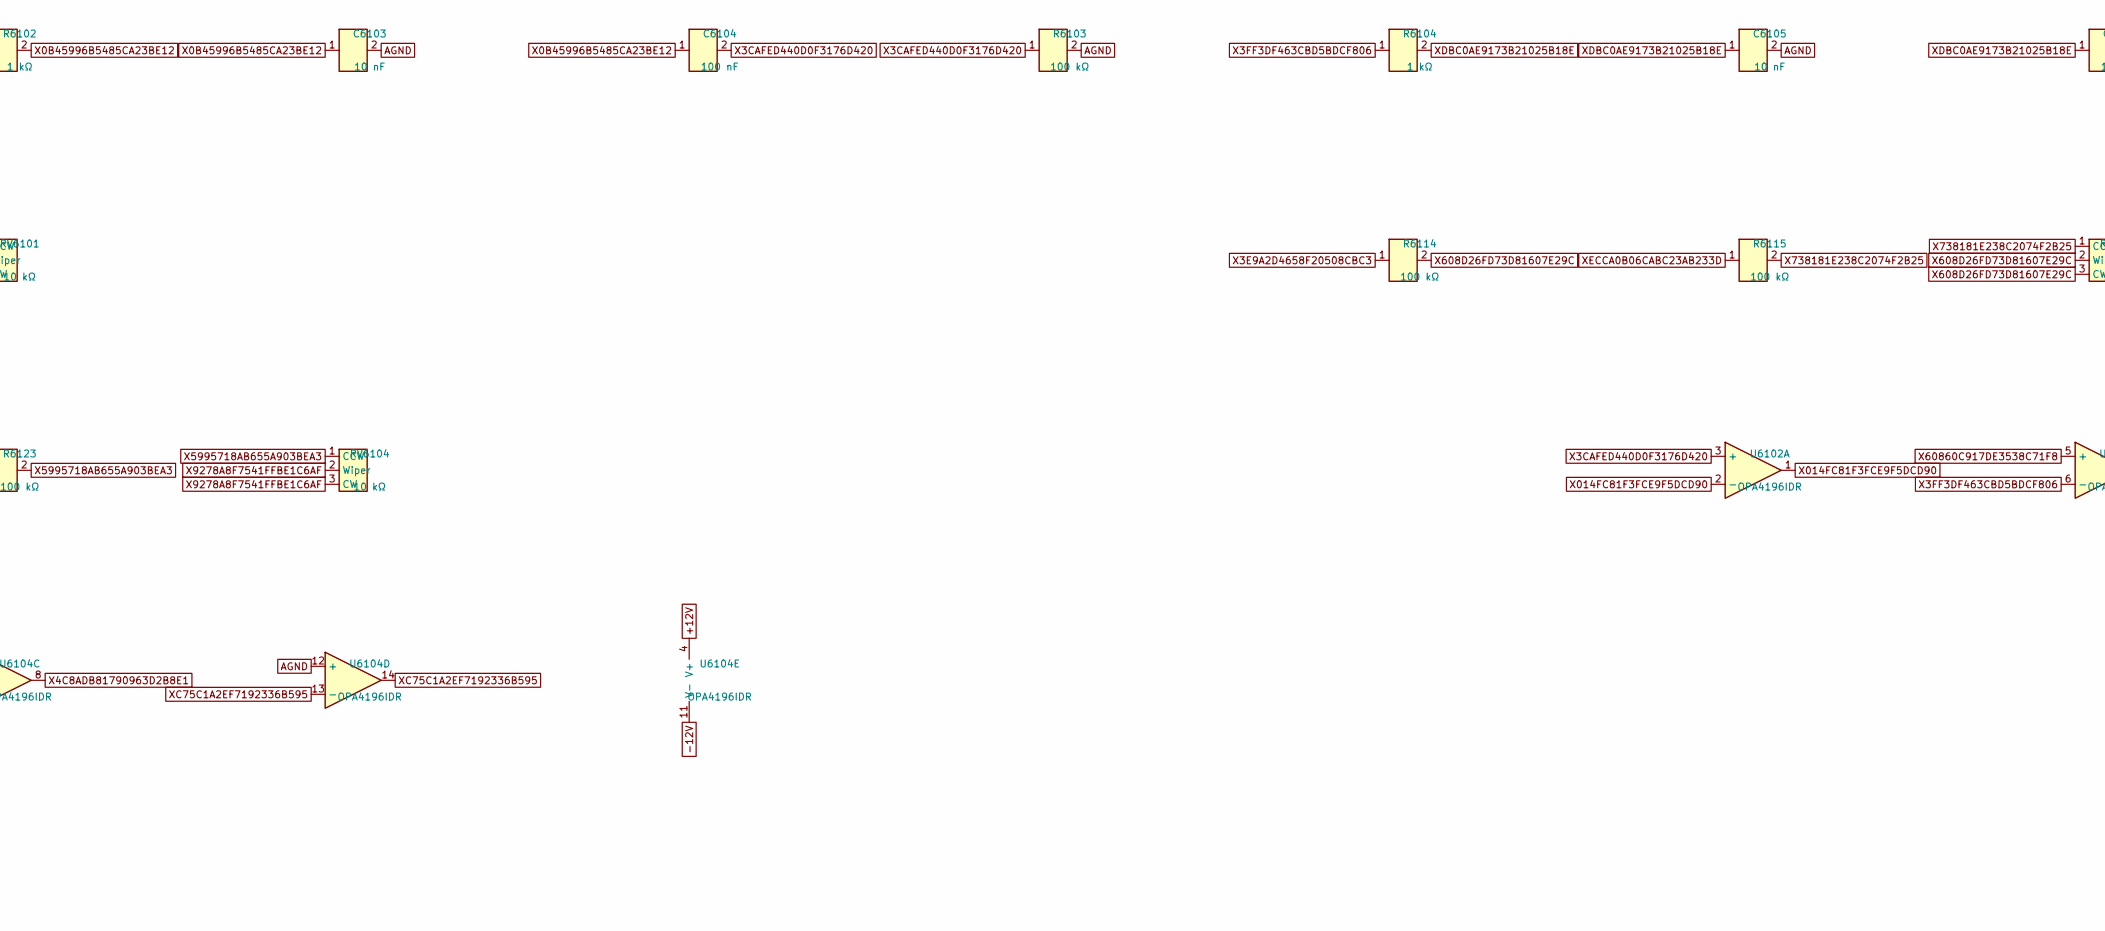
[picture p159: schematic noise_N1_K.kicad_sch, part in row 1, column 2]

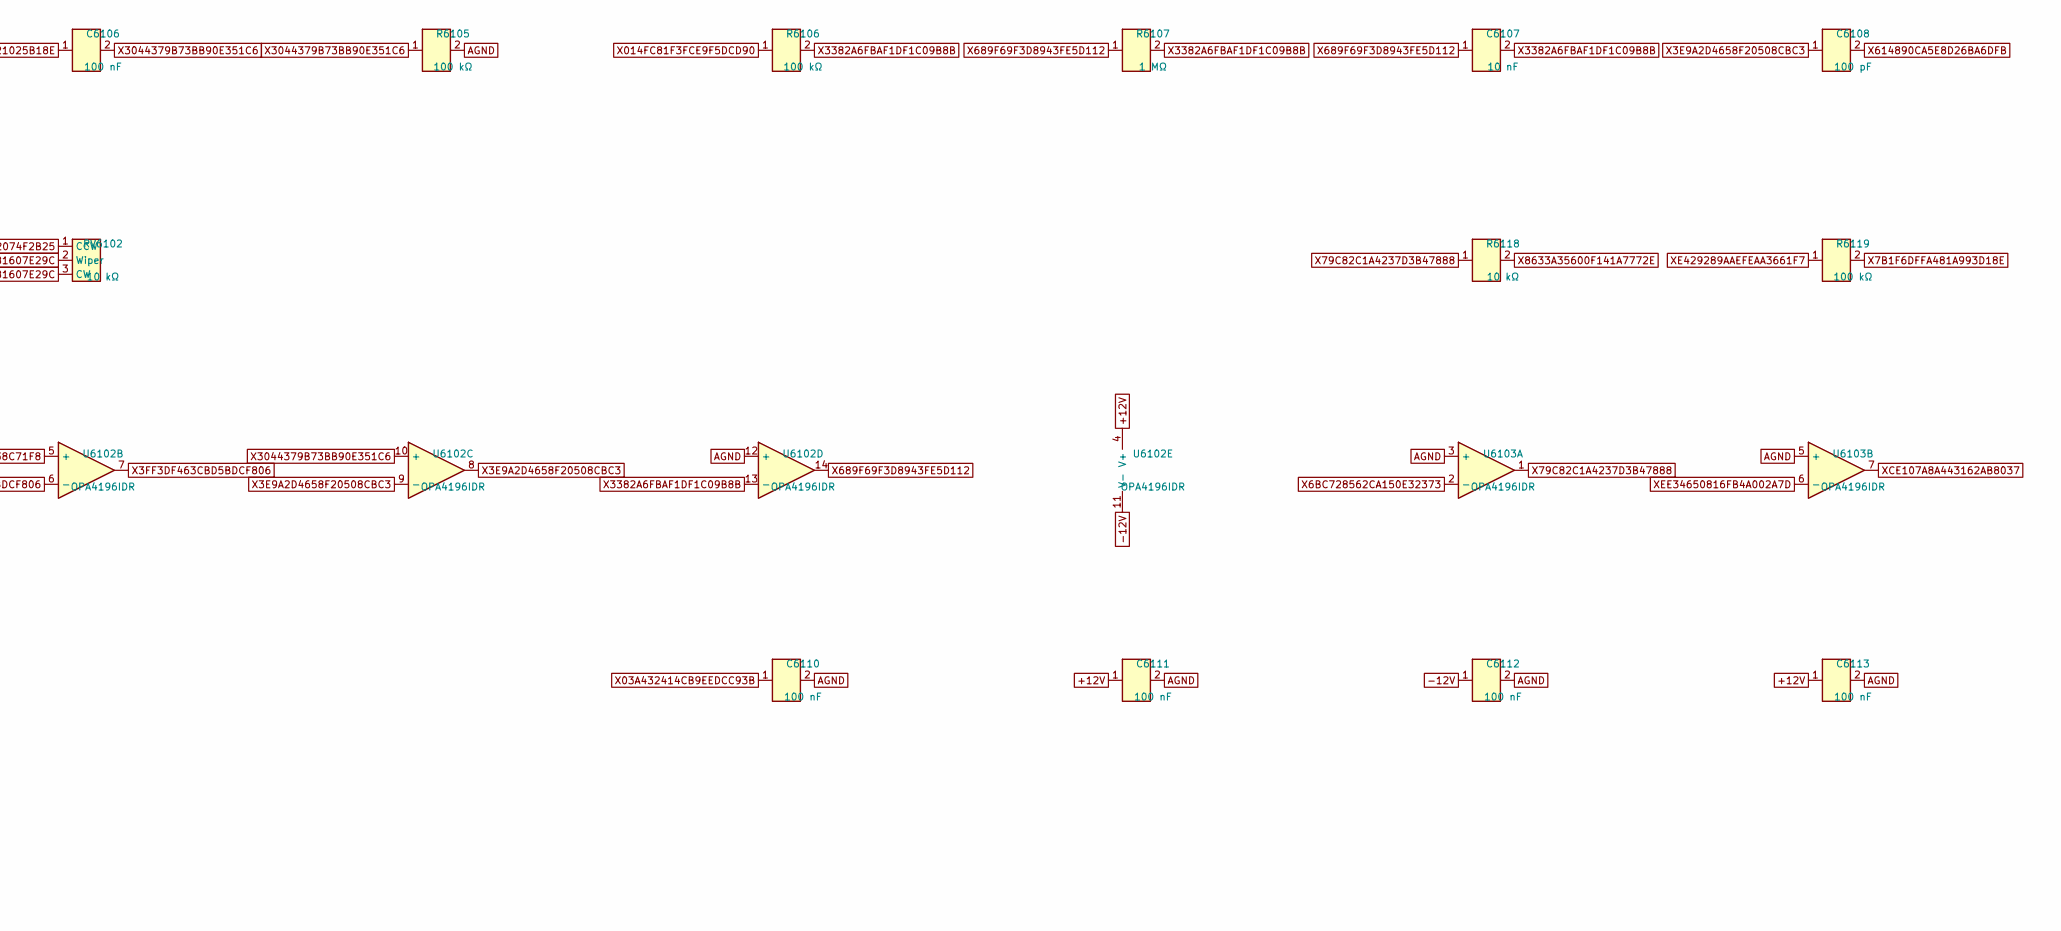
[picture p160: schematic noise_N1_K.kicad_sch, part in row 1, column 3]

Parts:
C6101: 4.7 µF; C0603
C6102, C6104, C6106, C6110, C6111, C6112, C6113, C6114, C6115, C6116: 100 nF; C0603; MPN GRM188R71H104KA93D
C6103, C6105, C6107: 10 nF; C0603
C6108: 100 pF; C0603; MPN C0603C101J5GACTU
C6109: 33 pF; C0603
R6101: 22 Ω; R0603
R6102, R6104: 1 kΩ; R0603
R6103, R6105, R6106, R6108, R6109, R6110, R6111, R6114, R6115, R6119, R6123: 100 kΩ; R0603; MPN RT0603BRD07100KL
R6107: 1 MΩ; R0603
R6118: 10 kΩ; R0603
R6122: 20 kΩ; R0603
RV6101, RV6102, RV6103, RV6104: 10 kΩ; Potentiometer_Bourns_TC33X_Vertical; MPN TC33X-2-103E
U6101: NOISE2; DIP-8_W7.62mm; MPN NOISE2
U6102, U6103, U6104: OPA4196IDR; SOIC-14_3.9x8.7mm_P1.27mm; MPN OPA4196IDR; LCSC C2057385

Connections:
+5V: R6101.1
+12V: C6111.1, C6113.1, C6115.1, U6102.4 (V+), U6103.4 (V+), U6104.4 (V+)
-12V: C6112.1, C6114.1, C6116.1, U6102.11 (V-), U6103.11 (V-), U6104.11 (V-)
AGND: C6101.2, C6102.2, C6103.2, C6105.2, C6110.2, C6111.2, C6112.2, C6113.2, C6114.2, C6115.2, C6116.2, R6103.2, R6105.2, U6101.2 (Unused), U6101.4 (Unused), U6101.5 (Unused), U6101.6 (Unused), U6101.8 (0V), U6102.12 (+), U6103.3 (+), U6103.5 (+), U6103.10 (+), U6103.12 (+), U6104.3 (+), U6104.5 (+), U6104.10 (+), U6104.12 (+)
X0B45996B5485CA23BE12: C6103.1, C6104.1, R6102.2
X2DF6A607443BC176057A: R6102.1, U6101.3 (WHITE OUT)
X03A432414CB9EEDCC93B: C6101.1, C6102.1, C6110.1, R6101.2, U6101.1 (+5V)
X3CAFED440D0F3176D420: C6104.2, R6103.1, U6102.3 (+)
X3E9A2D4658F20508CBC3: C6108.1, R6114.1, U6102.8, U6102.9 (-)
X3FF3DF463CBD5BDCF806: R6104.1, U6102.6 (-), U6102.7
X4C8ADB81790963D2B8E1: U6104.8, U6104.9 (-)
X6BC728562CA150E32373: C6109.2, R6108.2, R6109.2, U6103.2 (-)
X7B1F6DFFA481A993D18E: R6119.2, RV6103.1 (CCW)
X014FC81F3FCE9F5DCD90: R6106.1, R6110.1, U6102.1, U6102.2 (-)
X79C82C1A4237D3B47888: C6109.1, R6109.1, R6118.1, U6103.1
X608D26FD73D81607E29C: R6114.2, RV6102.2 (Wiper), RV6102.3 (CW), U6103.9 (-)
X689F69F3D8943FE5D112: C6107.1, R6107.1, R6122.1, U6102.14
X3382A6FBAF1DF1C09B8B: C6107.2, R6106.2, R6107.2, U6102.13 (-)
X8633A35600F141A7772E: R6118.2, RV6103.2 (Wiper), RV6103.3 (CW), U6103.13 (-)
X9278A8F7541FFBE1C6AF: R6122.2, RV6104.2 (Wiper), RV6104.3 (CW), U6104.2 (-)
X60860C917DE3538C71F8: U6101.7 (PINK OUT), U6102.5 (+)
X614890CA5E8D26BA6DFB: C6108.2, R6108.1
X738181E238C2074F2B25: R6115.2, RV6102.1 (CCW)
X3044379B73BB90E351C6: C6106.2, R6105.1, U6102.10 (+)
X5995718AB655A903BEA3: R6123.2, RV6104.1 (CCW)
XA97921AE972567EF91DF: R6123.1, U6104.1
XAB634879501F76B7EB22: U6104.6 (-), U6104.7
XC75C1A2EF7192336B595: U6104.13 (-), U6104.14
XCE107A8A443162AB8037: R6111.1, U6103.7
XDBC0AE9173B21025B18E: C6105.1, C6106.1, R6104.2
XE429289AAEFEAA3661F7: R6119.1, U6103.14
XECCA0B06CABC23AB233D: R6115.1, U6103.8
XEE34650816FB4A002A7D: R6110.2, RV6101.2 (Wiper), RV6101.3 (CW), U6103.6 (-)
XFDA935B1C162E7FE0831: R6111.2, RV6101.1 (CCW)
