Takazudo/zudo-osc-hole-field/boards/osc-core/sheets/offset_A01_K.kicad_sch

## KiCad design boards/osc-core/sheets/offset_A01_K.kicad_sch (2026-10-05)

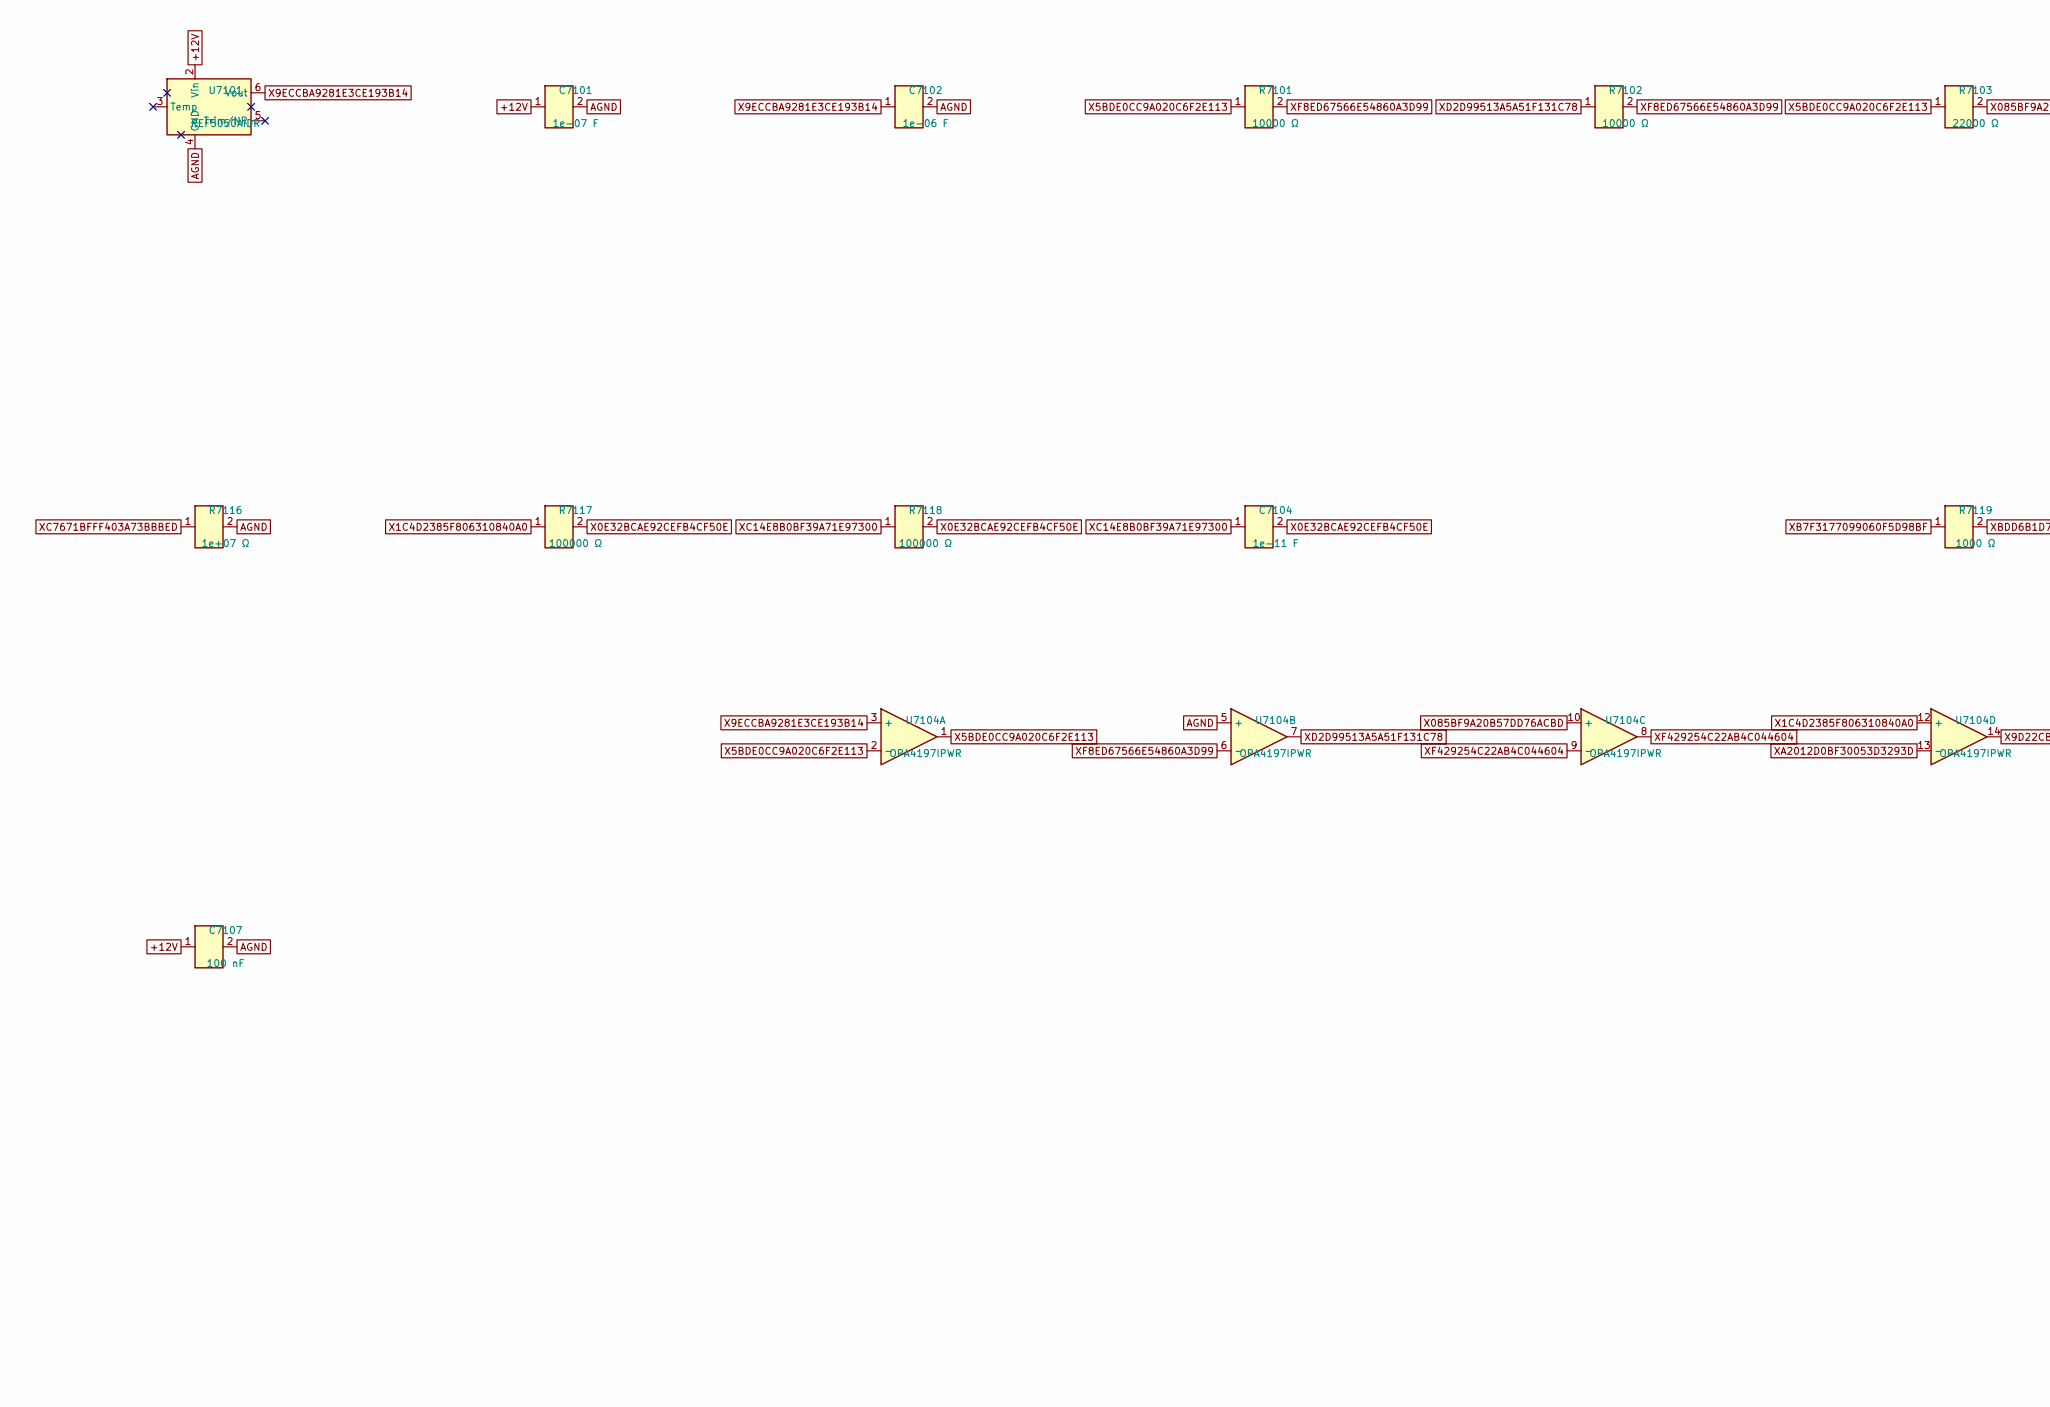
[picture p161: schematic offset_A01_K.kicad_sch, part in row 1, column 1]

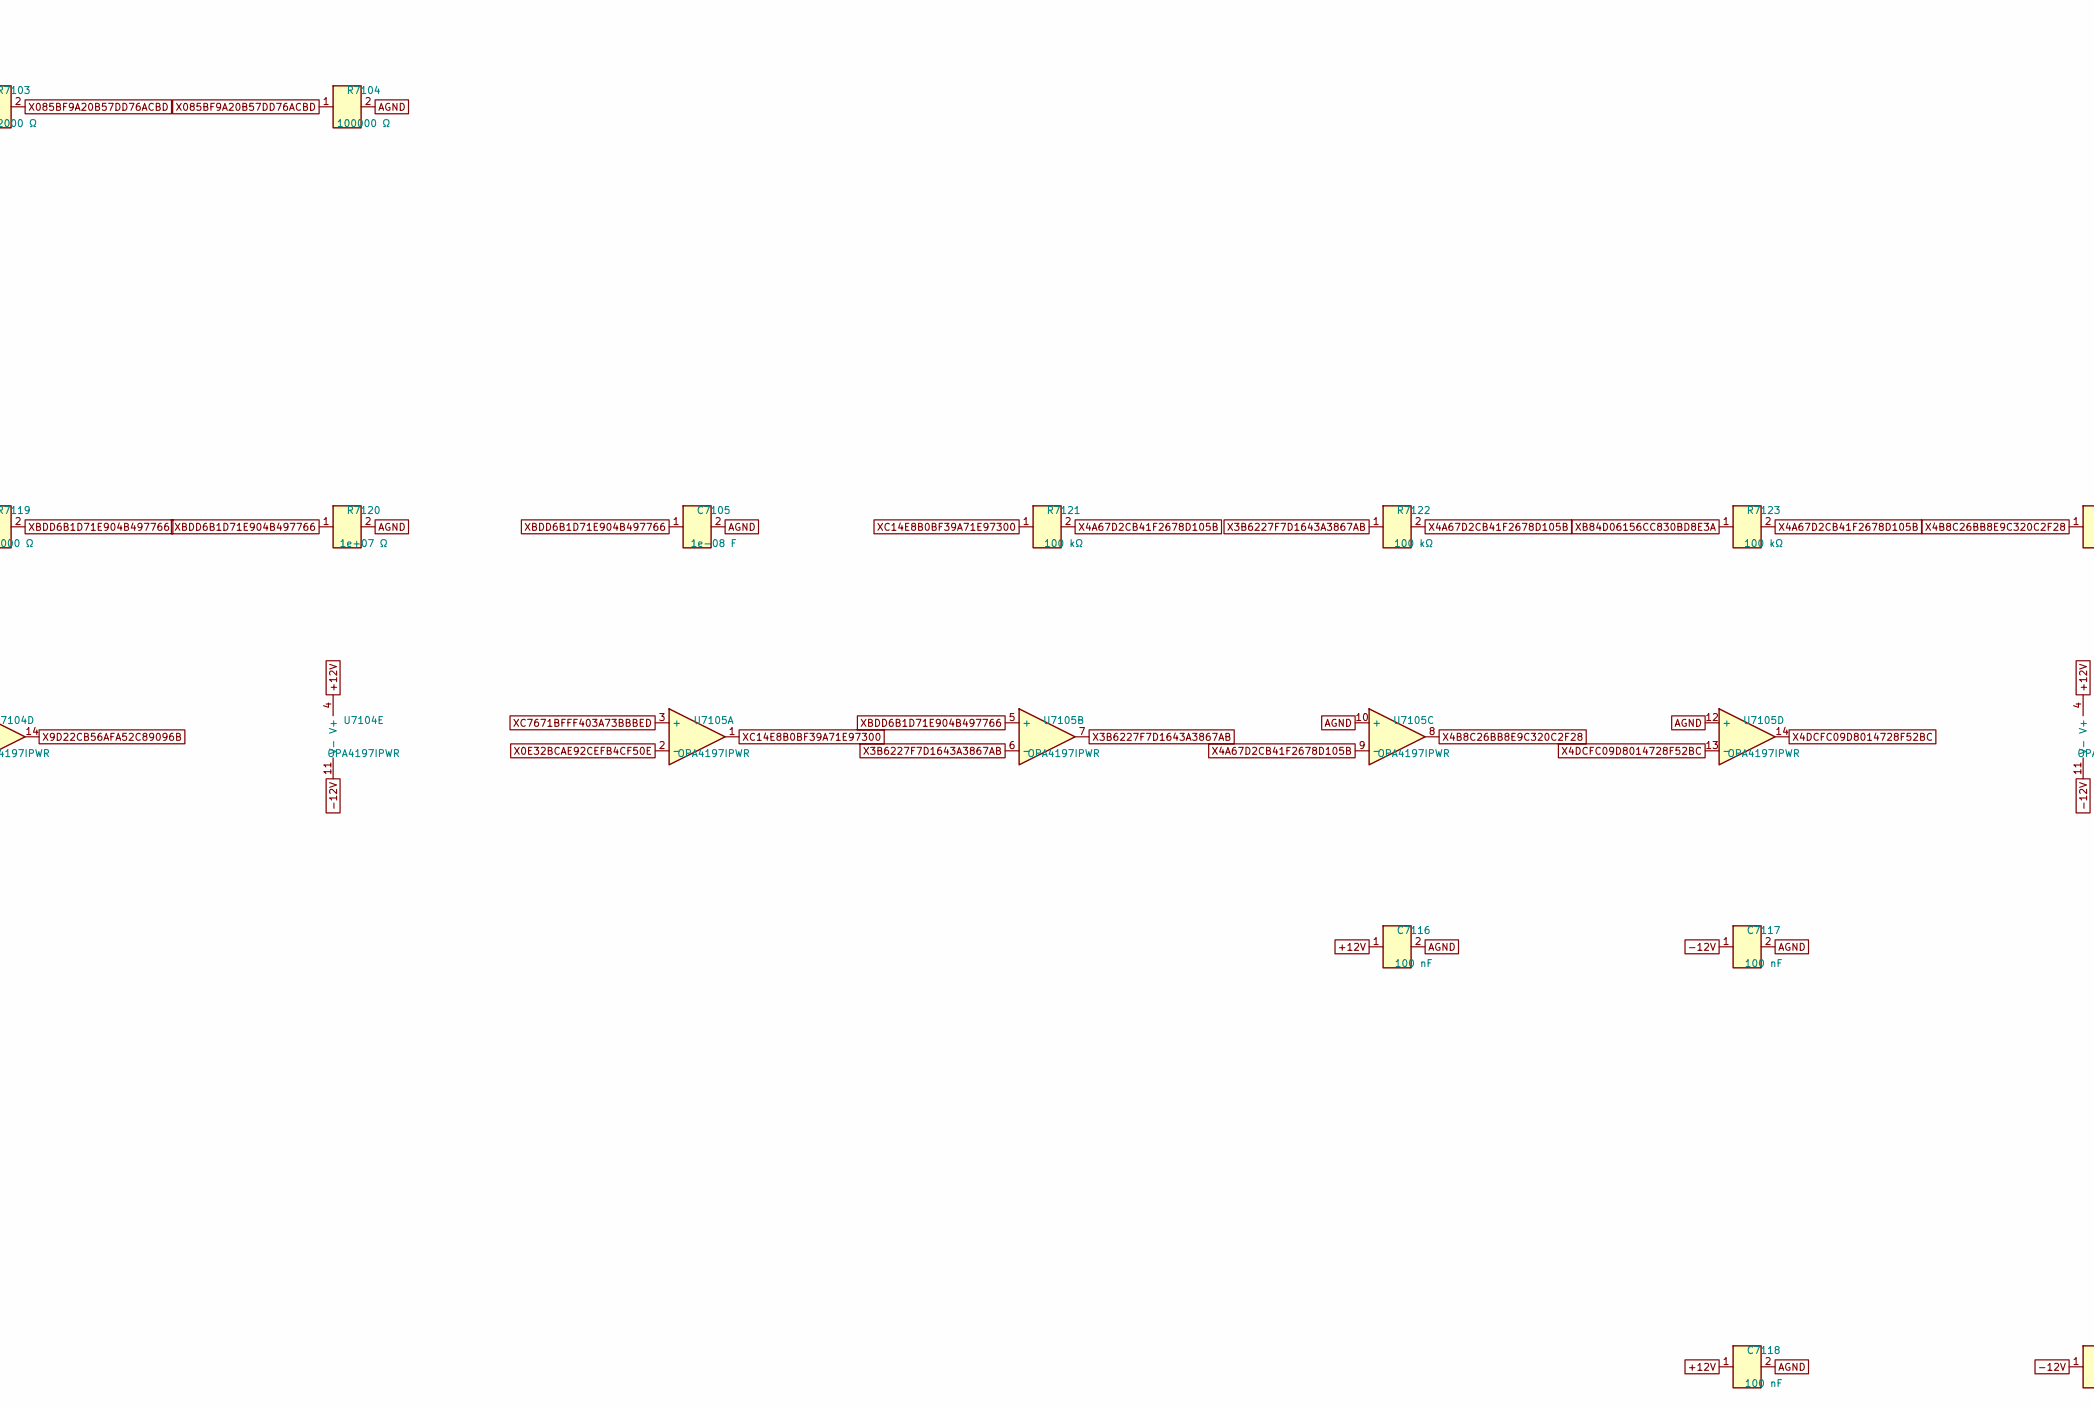
[picture p162: schematic offset_A01_K.kicad_sch, part in row 1, column 2]

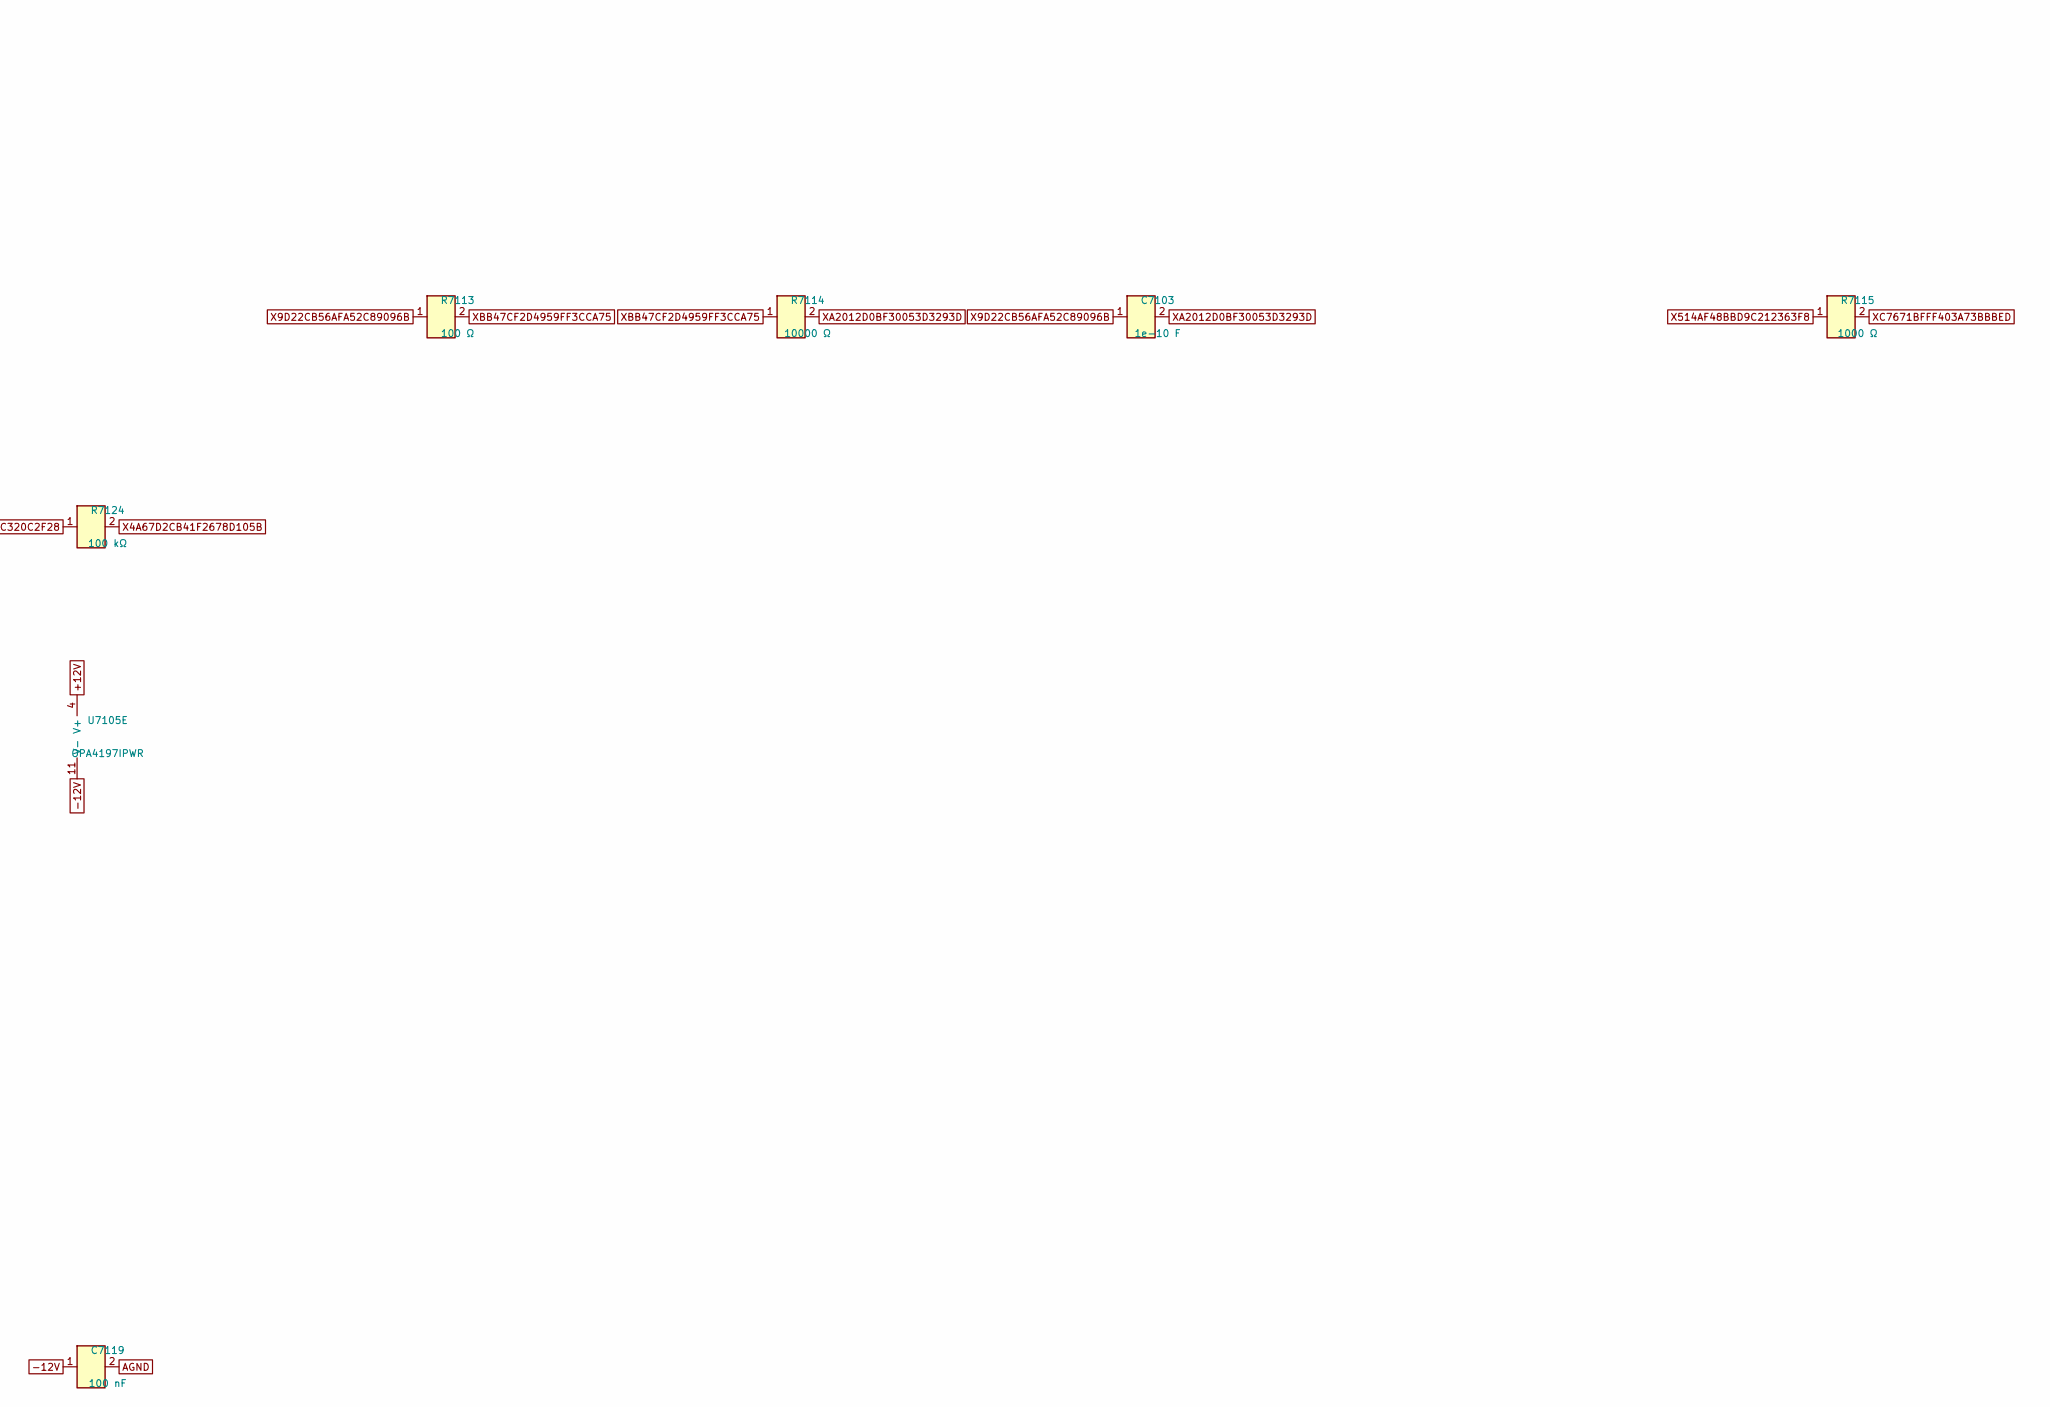
[picture p163: schematic offset_A01_K.kicad_sch, part in row 1, column 3]

Parts:
C7101: 1e-07 F; C0603; MPN GRM188R71H104KA93D
C7102: 1e-06 F; C0603
C7103: 1e-10 F; C0603; MPN C0603C101J5GACTU
C7104: 1e-11 F; C0603
C7105: 1e-08 F; C0603
C7107, C7116, C7117, C7118, C7119: 100 nF; C0603; MPN GRM188R71H104KA93D
R7101, R7102, R7114: 10000 Ω; R0603
R7103: 22000 Ω; R0603
R7104, R7117, R7118: 100000 Ω; R0603; MPN RT0603BRD07100KL
R7113: 100 Ω; R0603
R7115, R7119: 1000 Ω; R0603
R7116, R7120: 1e+07 Ω; R0603
R7121, R7122, R7123, R7124: 100 kΩ; R0603; MPN RT0603BRD07100KL
U7101: REF5050AIDR; SOIC-8_3.9x4.9mm_P1.27mm; MPN REF5050AIDR; LCSC C27804
U7104, U7105: OPA4197IPWR; TSSOP-14_4.4x5mm_P0.65mm; MPN OPA4197IPWR; LCSC C2057327

Connections:
+12V: C7101.1, C7107.1, C7116.1, C7118.1, U7101.2 (Vin), U7104.4 (V+), U7105.4 (V+)
-12V: C7117.1, C7119.1, U7104.11 (V-), U7105.11 (V-)
AGND: C7101.2, C7102.2, C7105.2, C7107.2, C7116.2, C7117.2, C7118.2, C7119.2, R7104.2, R7116.2, R7120.2, U7101.4 (GND), U7104.5 (+), U7105.10 (+), U7105.12 (+)
X0E32BCAE92CEFB4CF50E: C7104.2, R7117.2, R7118.2, U7105.2 (-)
X1C4D2385F806310840A0: R7117.1, U7104.12 (+)
X3B6227F7D1643A3867AB: R7122.1, U7105.6 (-), U7105.7
X4A67D2CB41F2678D105B: R7121.2, R7122.2, R7123.2, R7124.2, U7105.9 (-)
X4B8C26BB8E9C320C2F28: R7124.1, U7105.8
X4DCFC09D8014728F52BC: U7105.13 (-), U7105.14
X5BDE0CC9A020C6F2E113: R7101.1, R7103.1, U7104.1, U7104.2 (-)
X9D22CB56AFA52C89096B: C7103.1, R7113.1, U7104.14
X9ECCBA9281E3CE193B14: C7102.1, U7101.6 (Vout), U7104.3 (+)
X085BF9A20B57DD76ACBD: R7103.2, R7104.1, U7104.10 (+)
X514AF48BBD9C212363F8: R7115.1
XA2012D0BF30053D3293D: C7103.2, R7114.2, U7104.13 (-)
XB7F3177099060F5D98BF: R7119.1
XB84D06156CC830BD8E3A: R7123.1
XBB47CF2D4959FF3CCA75: R7113.2, R7114.1
XBDD6B1D71E904B497766: C7105.1, R7119.2, R7120.1, U7105.5 (+)
XC14E8B0BF39A71E97300: C7104.1, R7118.1, R7121.1, U7105.1
XC7671BFFF403A73BBBED: R7115.2, R7116.1, U7105.3 (+)
XD2D99513A5A51F131C78: R7102.1, U7104.7
XF8ED67566E54860A3D99: R7101.2, R7102.2, U7104.6 (-)
XF429254C22AB4C044604: U7104.8, U7104.9 (-)
