Takazudo/zudo-osc-hole-field/boards/osc-core/sheets/offset_A02_K.kicad_sch

## KiCad design boards/osc-core/sheets/offset_A02_K.kicad_sch (2026-10-05)

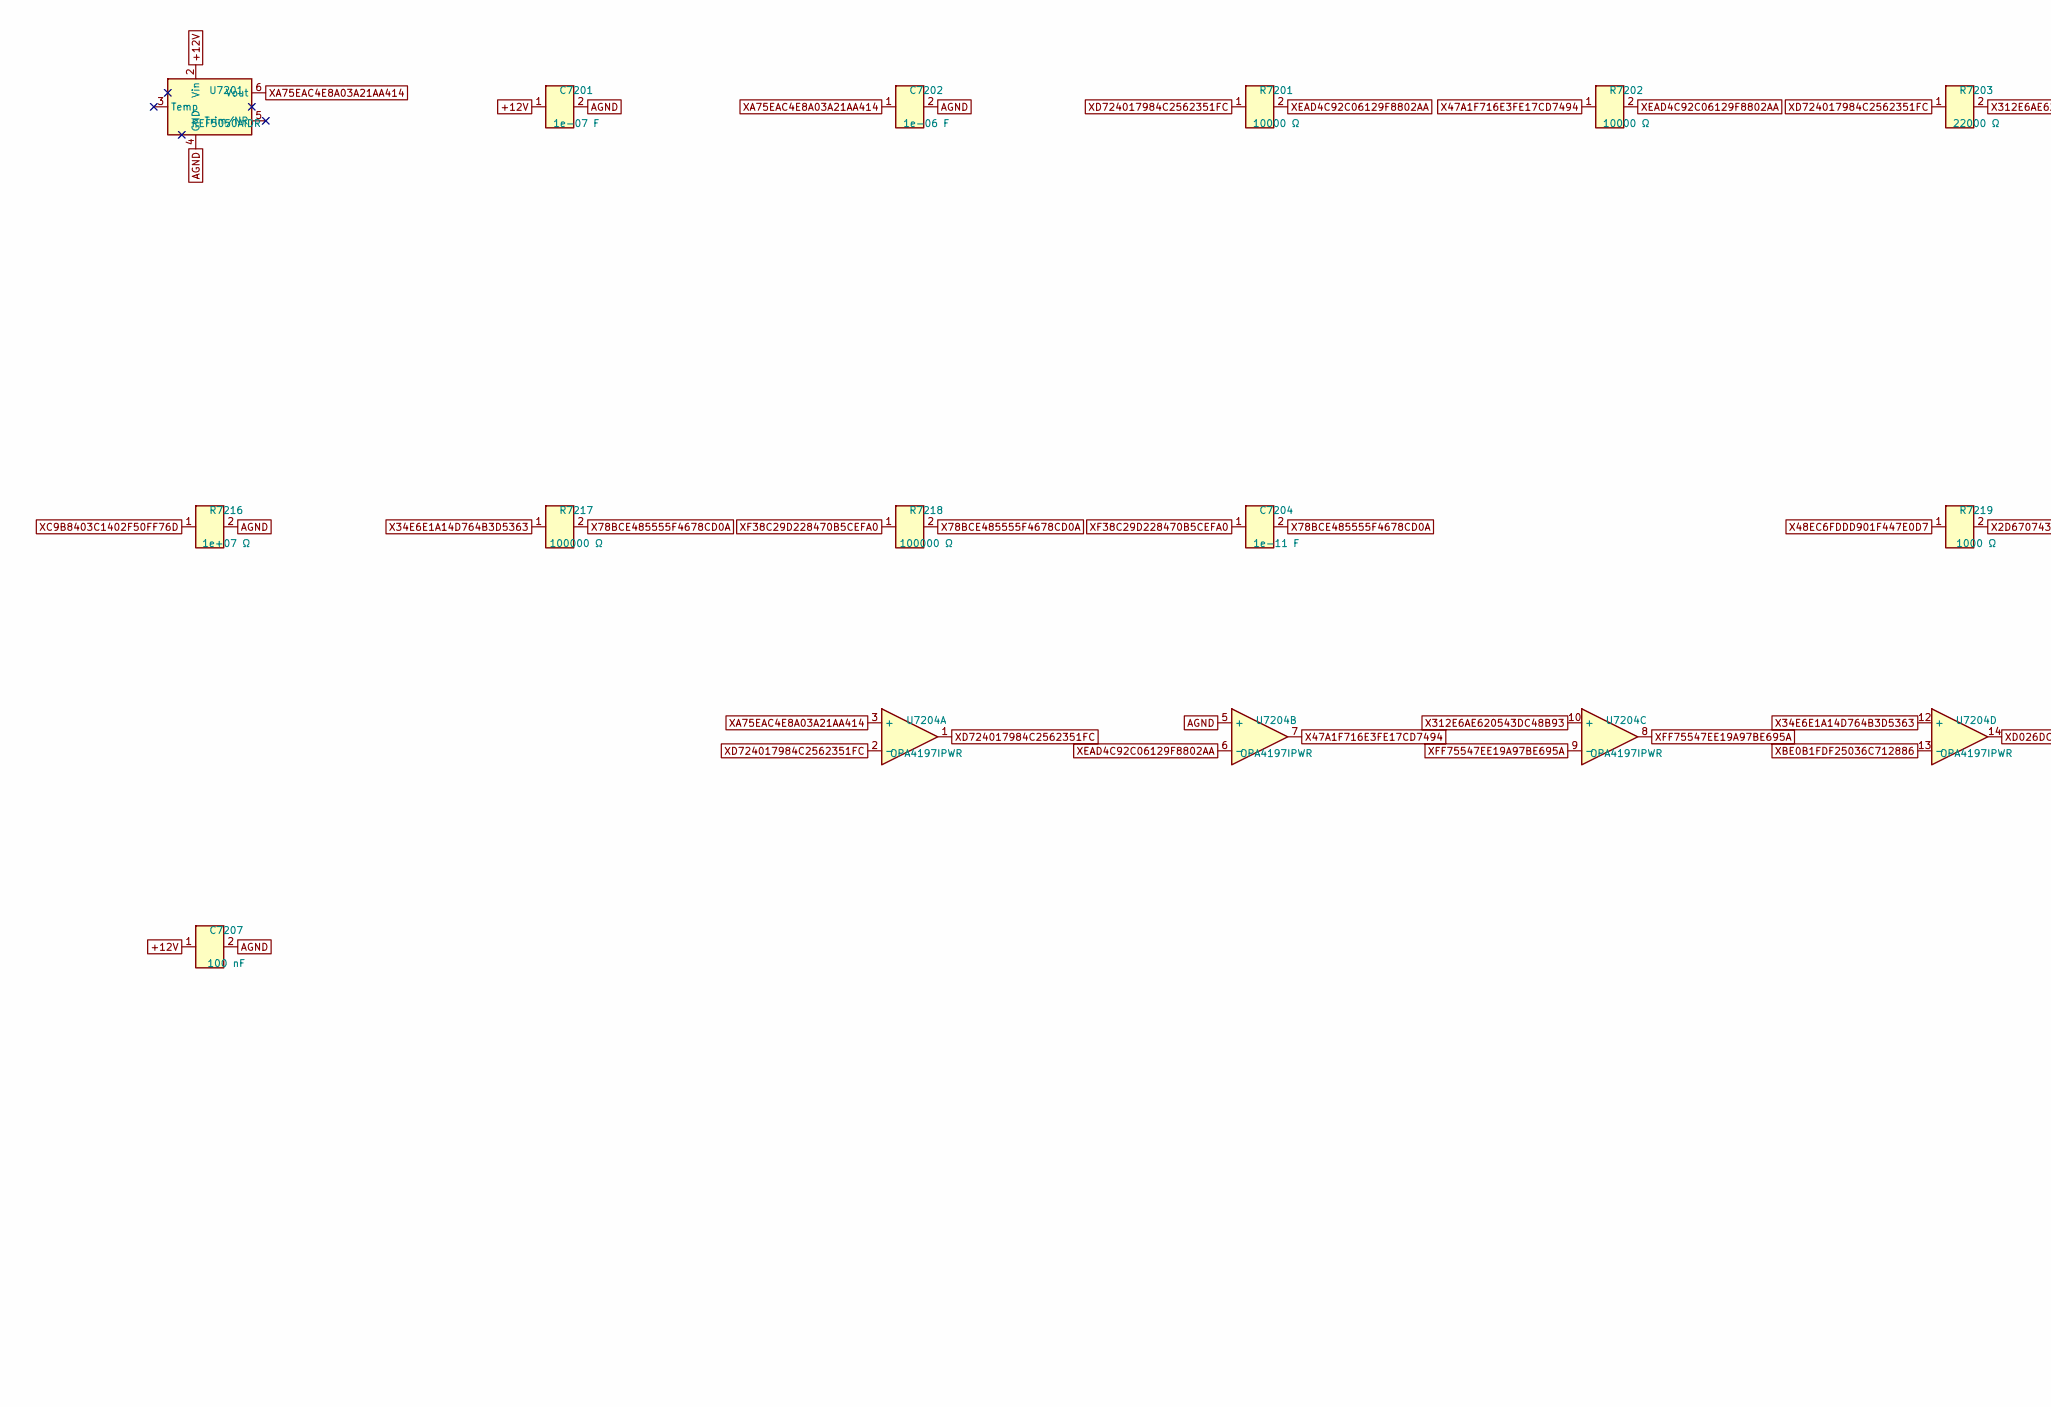
[picture p164: schematic offset_A02_K.kicad_sch, part in row 1, column 1]

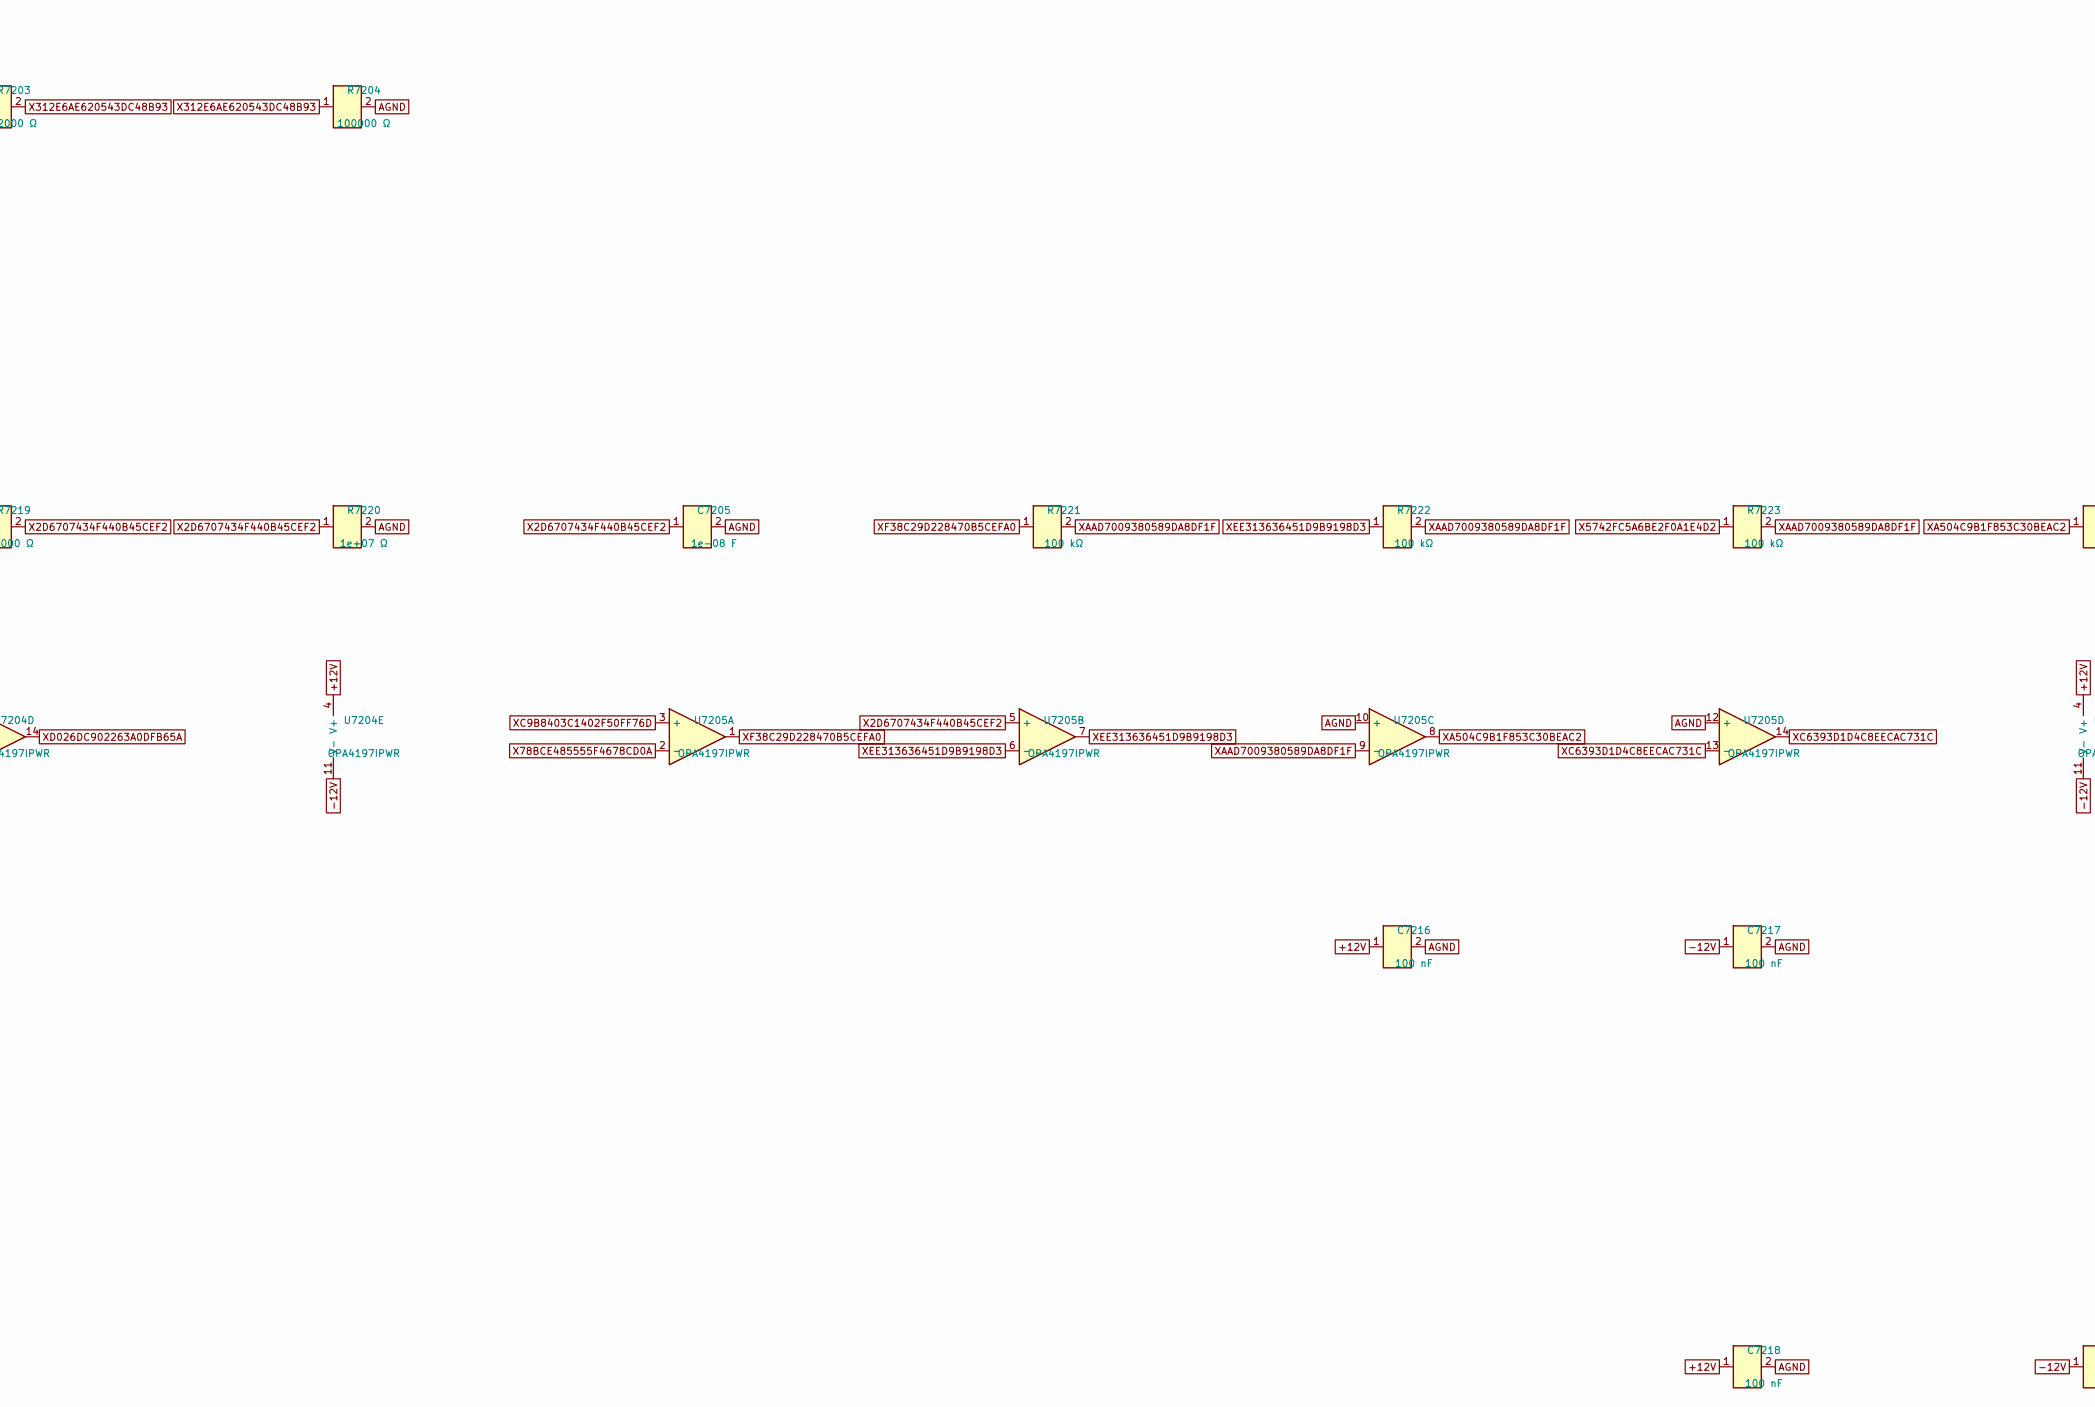
[picture p165: schematic offset_A02_K.kicad_sch, part in row 1, column 2]

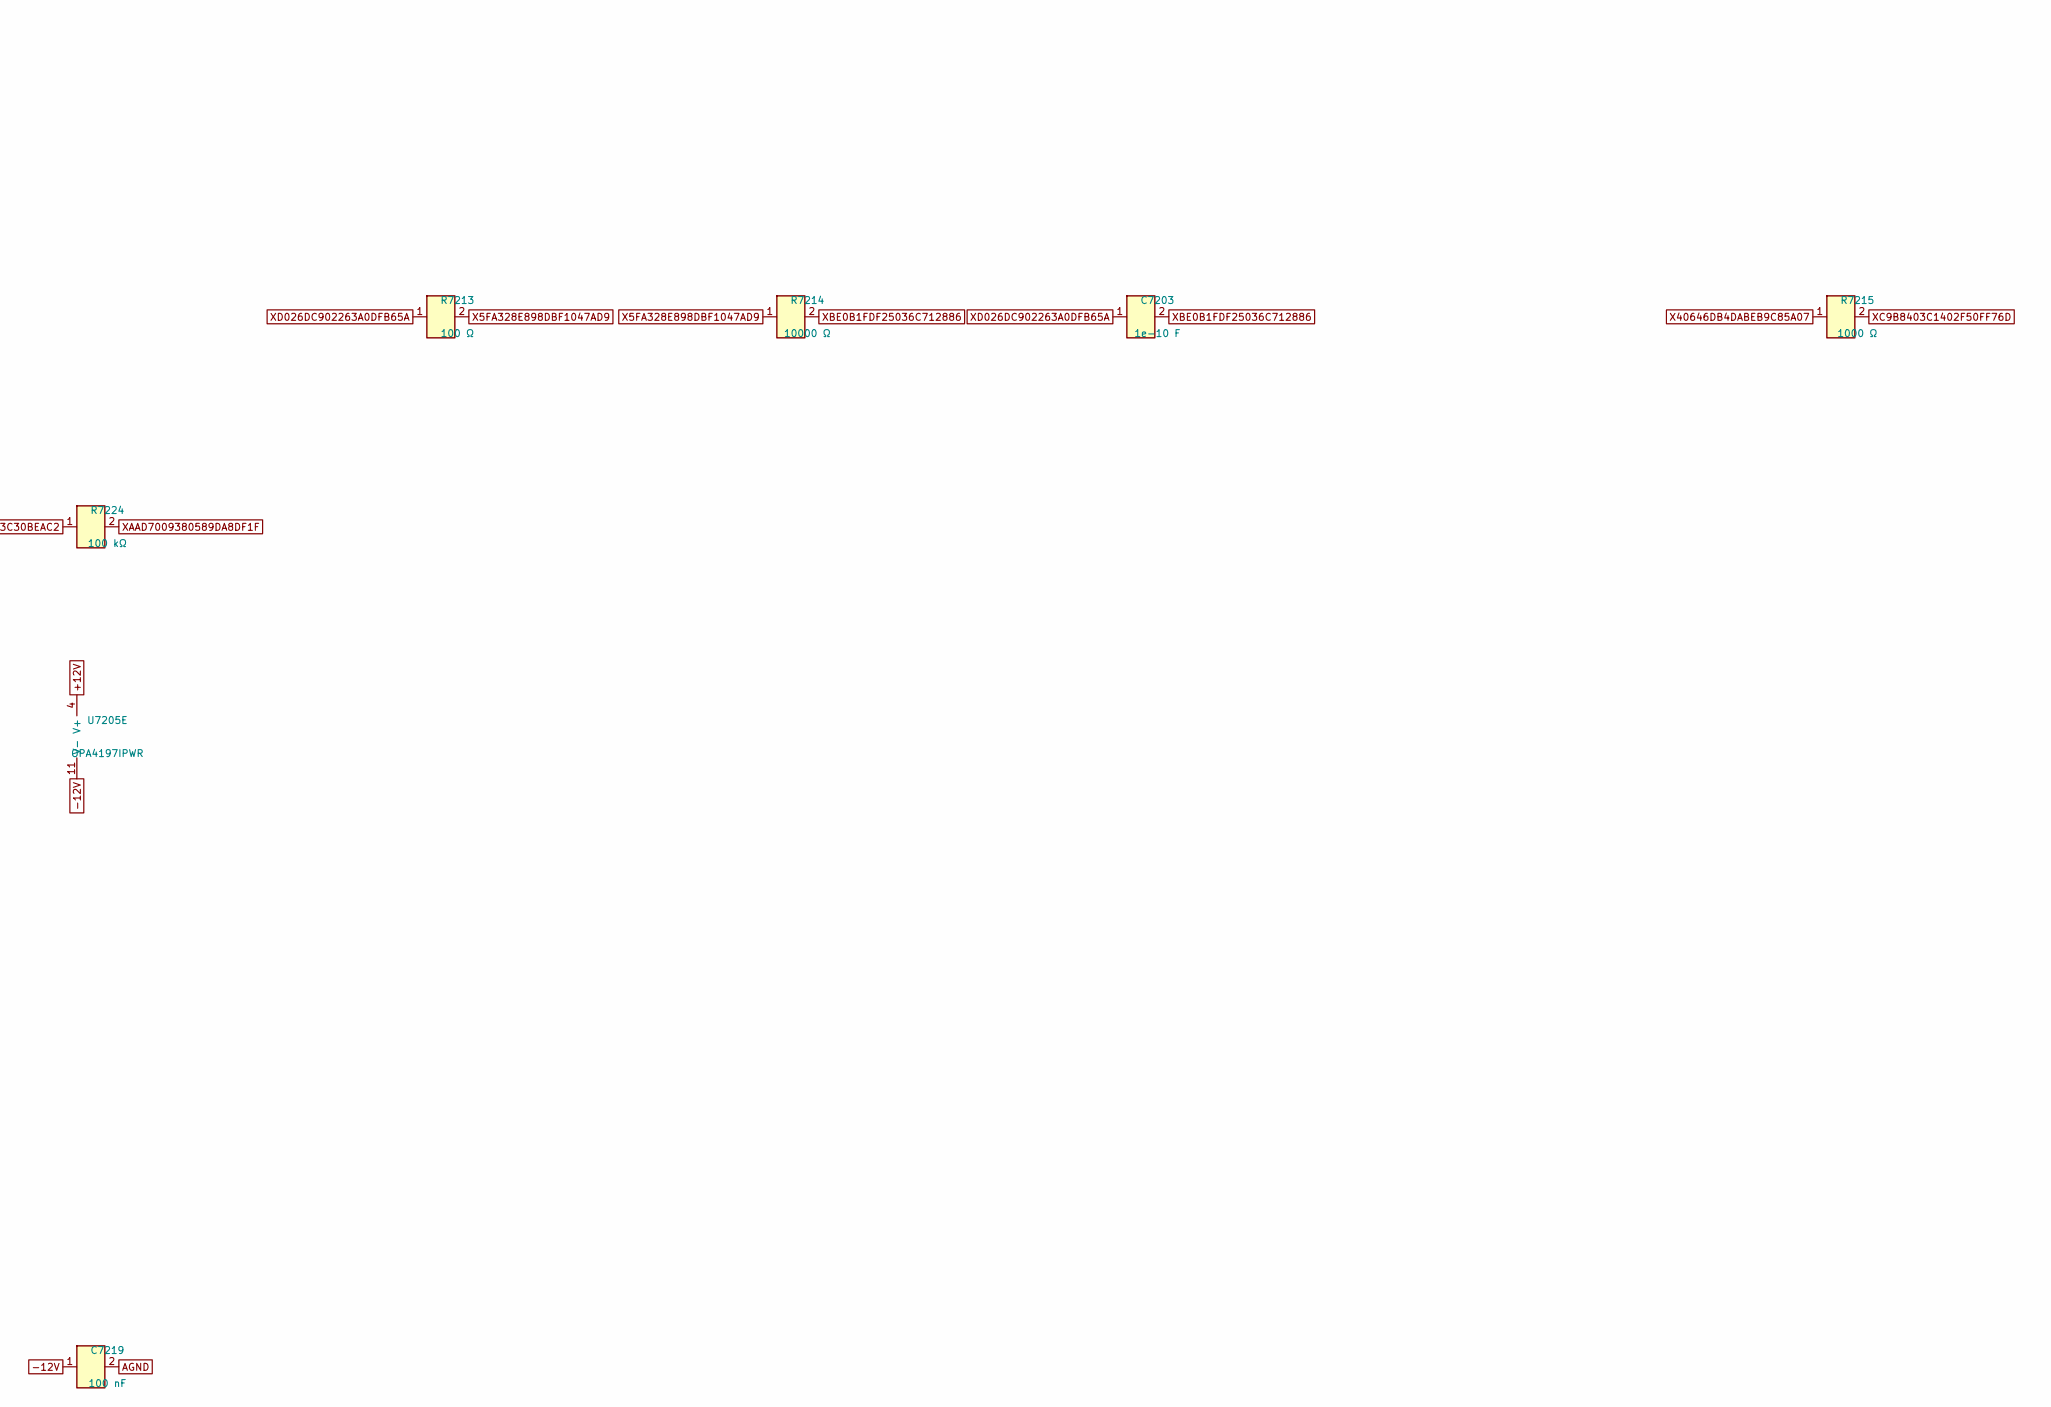
[picture p166: schematic offset_A02_K.kicad_sch, part in row 1, column 3]

Parts:
C7201: 1e-07 F; C0603; MPN GRM188R71H104KA93D
C7202: 1e-06 F; C0603
C7203: 1e-10 F; C0603; MPN C0603C101J5GACTU
C7204: 1e-11 F; C0603
C7205: 1e-08 F; C0603
C7207, C7216, C7217, C7218, C7219: 100 nF; C0603; MPN GRM188R71H104KA93D
R7201, R7202, R7214: 10000 Ω; R0603
R7203: 22000 Ω; R0603
R7204, R7217, R7218: 100000 Ω; R0603; MPN RT0603BRD07100KL
R7213: 100 Ω; R0603
R7215, R7219: 1000 Ω; R0603
R7216, R7220: 1e+07 Ω; R0603
R7221, R7222, R7223, R7224: 100 kΩ; R0603; MPN RT0603BRD07100KL
U7201: REF5050AIDR; SOIC-8_3.9x4.9mm_P1.27mm; MPN REF5050AIDR; LCSC C27804
U7204, U7205: OPA4197IPWR; TSSOP-14_4.4x5mm_P0.65mm; MPN OPA4197IPWR; LCSC C2057327

Connections:
+12V: C7201.1, C7207.1, C7216.1, C7218.1, U7201.2 (Vin), U7204.4 (V+), U7205.4 (V+)
-12V: C7217.1, C7219.1, U7204.11 (V-), U7205.11 (V-)
AGND: C7201.2, C7202.2, C7205.2, C7207.2, C7216.2, C7217.2, C7218.2, C7219.2, R7204.2, R7216.2, R7220.2, U7201.4 (GND), U7204.5 (+), U7205.10 (+), U7205.12 (+)
X2D6707434F440B45CEF2: C7205.1, R7219.2, R7220.1, U7205.5 (+)
X5FA328E898DBF1047AD9: R7213.2, R7214.1
X34E6E1A14D764B3D5363: R7217.1, U7204.12 (+)
X47A1F716E3FE17CD7494: R7202.1, U7204.7
X48EC6FDDD901F447E0D7: R7219.1
X78BCE485555F4678CD0A: C7204.2, R7217.2, R7218.2, U7205.2 (-)
X312E6AE620543DC48B93: R7203.2, R7204.1, U7204.10 (+)
X5742FC5A6BE2F0A1E4D2: R7223.1
X40646DB4DABEB9C85A07: R7215.1
XA75EAC4E8A03A21AA414: C7202.1, U7201.6 (Vout), U7204.3 (+)
XA504C9B1F853C30BEAC2: R7224.1, U7205.8
XAAD7009380589DA8DF1F: R7221.2, R7222.2, R7223.2, R7224.2, U7205.9 (-)
XBE0B1FDF25036C712886: C7203.2, R7214.2, U7204.13 (-)
XC9B8403C1402F50FF76D: R7215.2, R7216.1, U7205.3 (+)
XC6393D1D4C8EECAC731C: U7205.13 (-), U7205.14
XD026DC902263A0DFB65A: C7203.1, R7213.1, U7204.14
XD724017984C2562351FC: R7201.1, R7203.1, U7204.1, U7204.2 (-)
XEAD4C92C06129F8802AA: R7201.2, R7202.2, U7204.6 (-)
XEE313636451D9B9198D3: R7222.1, U7205.6 (-), U7205.7
XF38C29D228470B5CEFA0: C7204.1, R7218.1, R7221.1, U7205.1
XFF75547EE19A97BE695A: U7204.8, U7204.9 (-)
