Takazudo/zudo-osc-hole-field/boards/osc-core/sheets/offset_A03_K.kicad_sch

## KiCad design boards/osc-core/sheets/offset_A03_K.kicad_sch (2026-10-05)

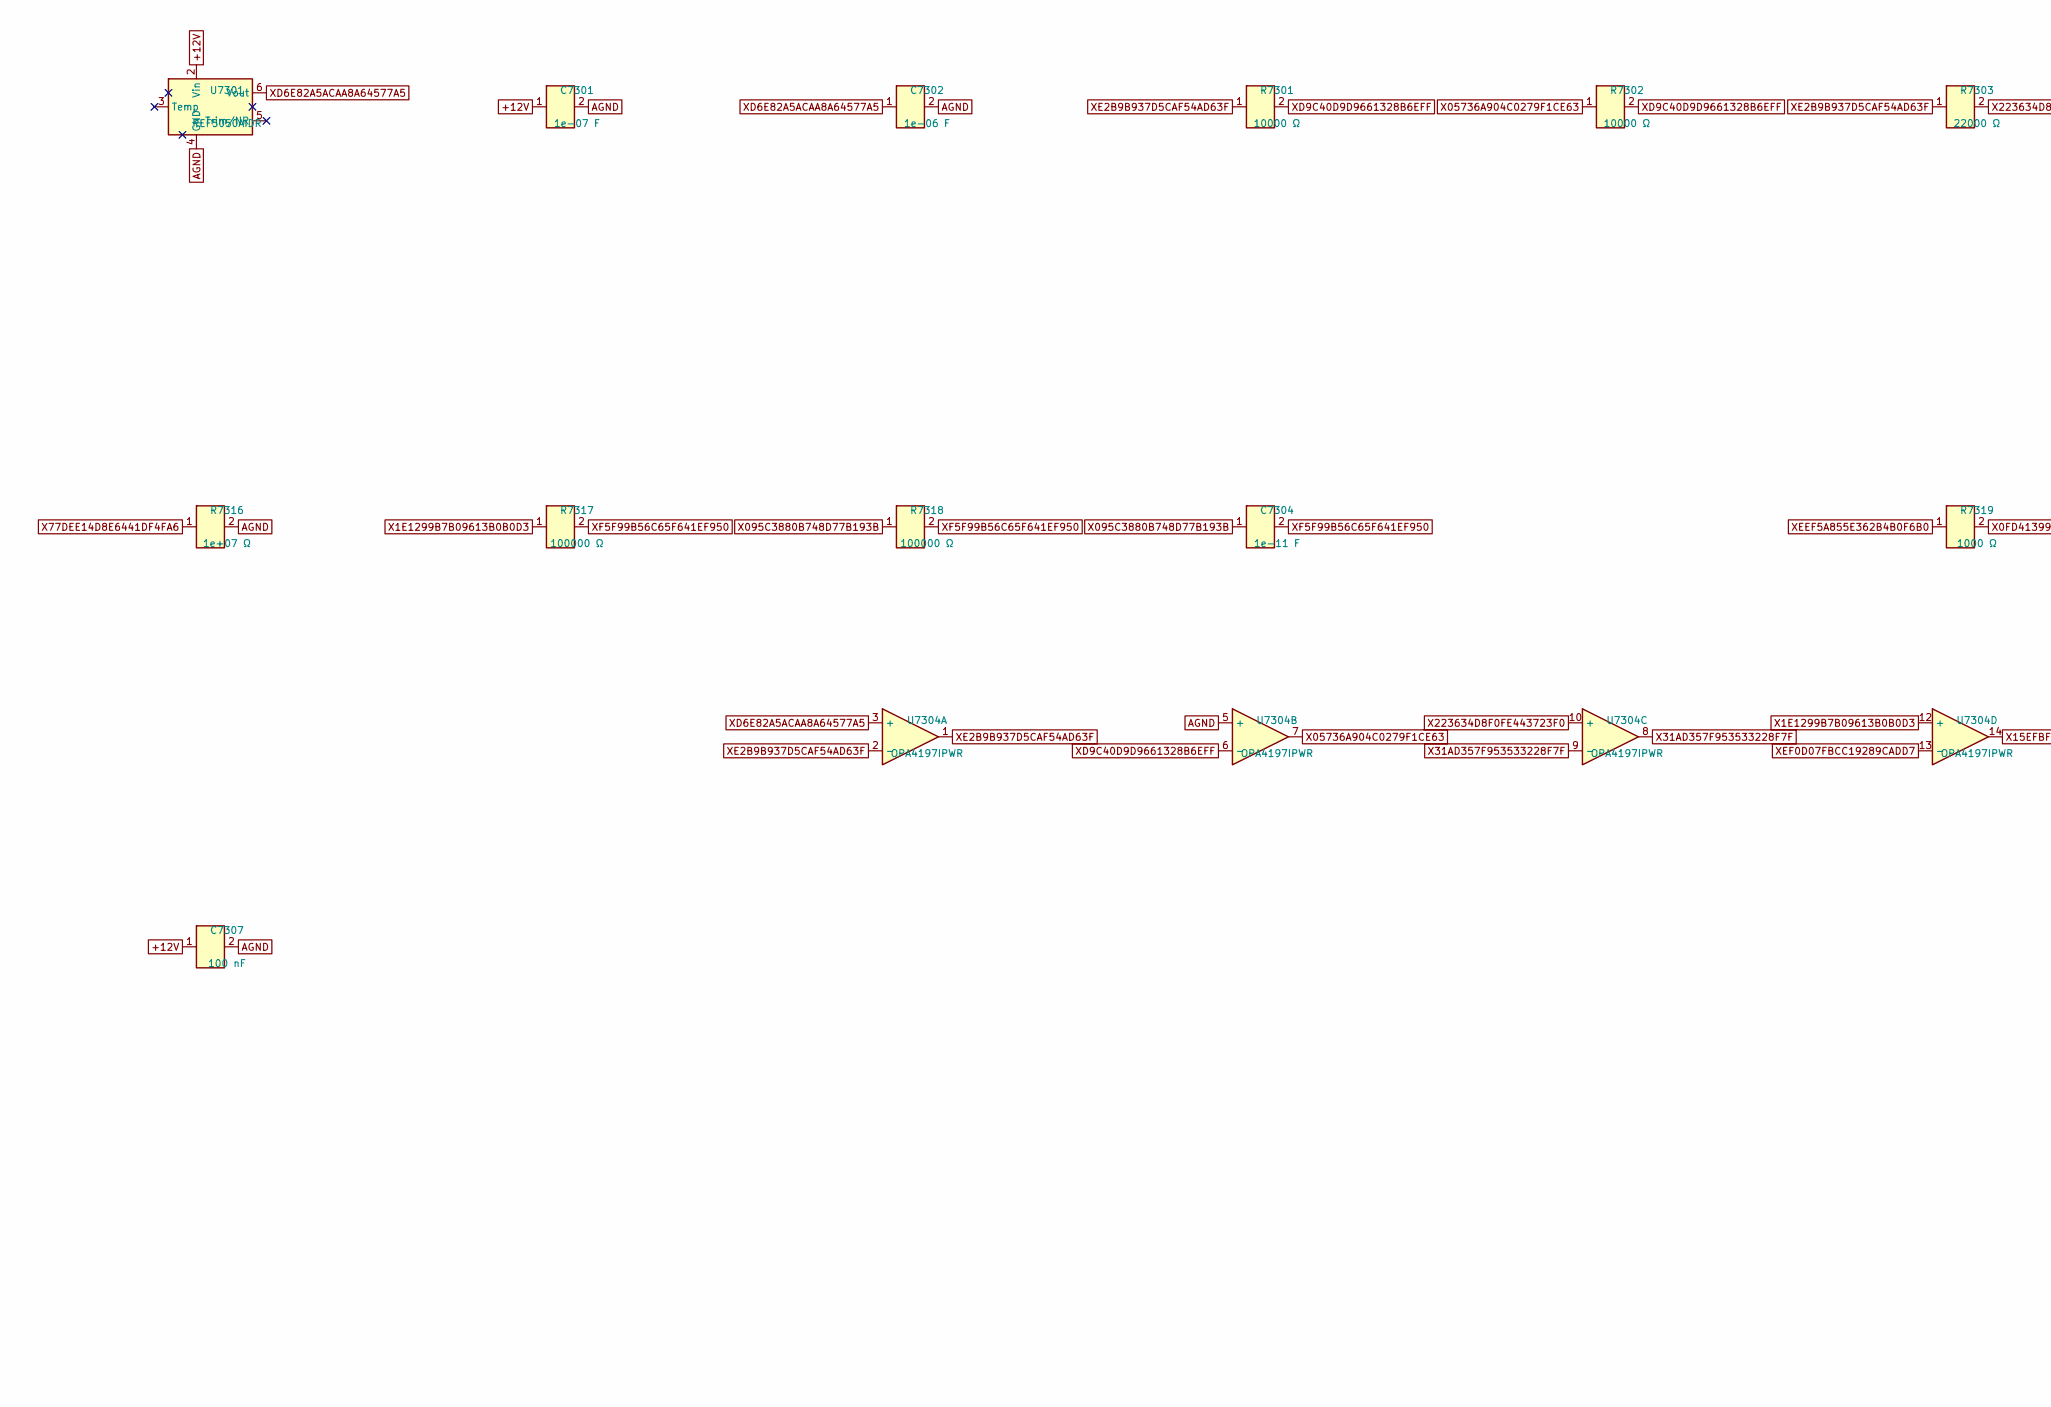
[picture p167: schematic offset_A03_K.kicad_sch, part in row 1, column 1]

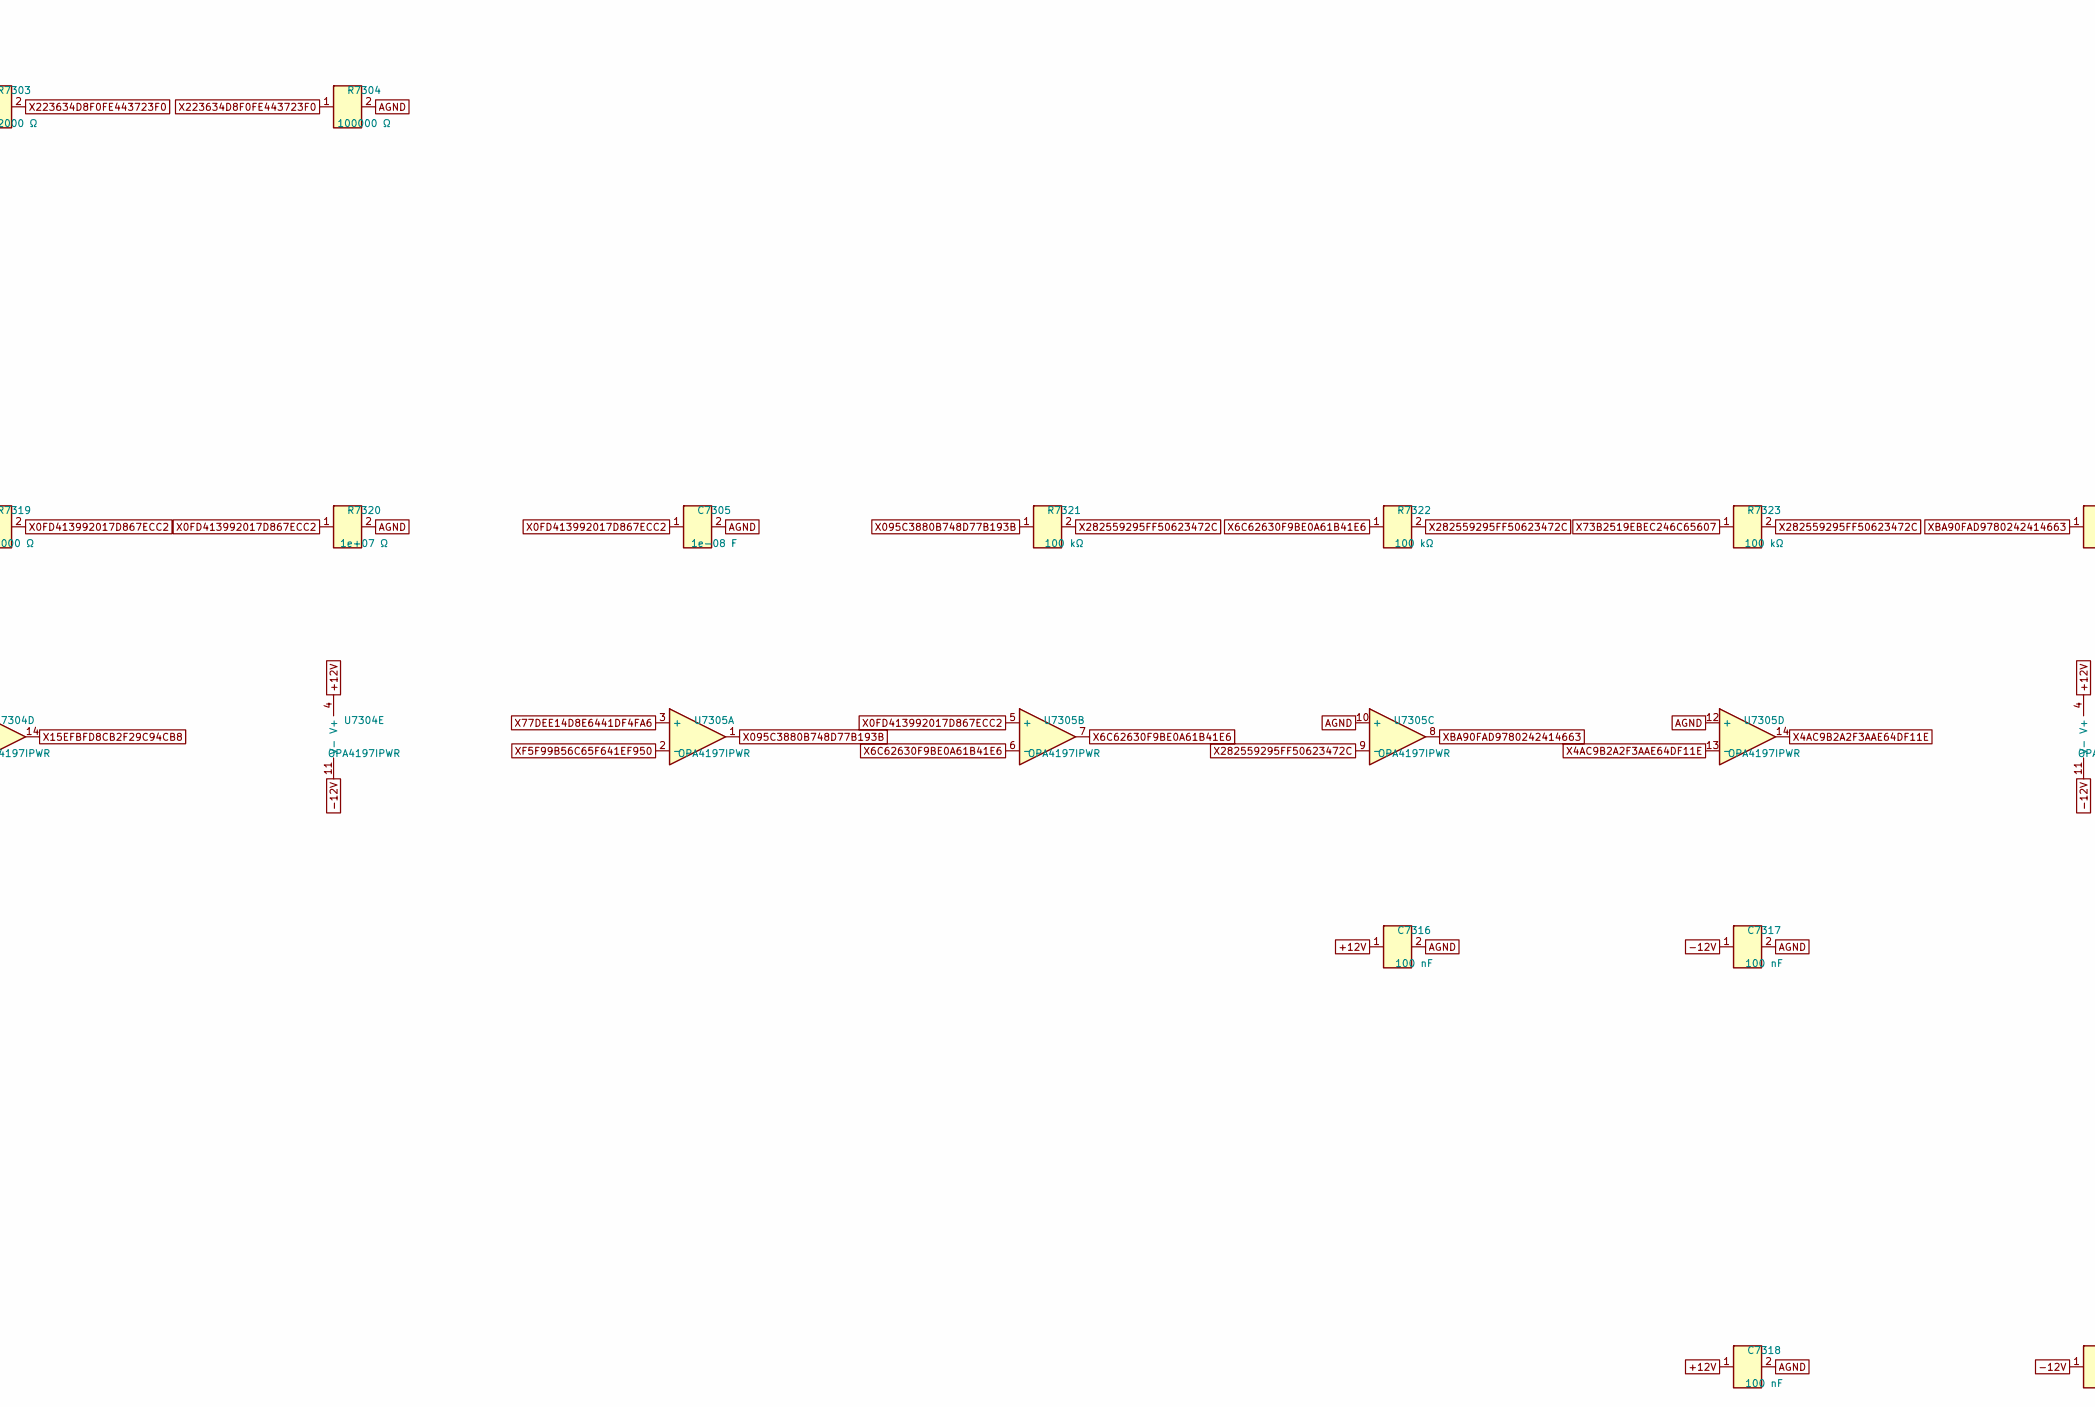
[picture p168: schematic offset_A03_K.kicad_sch, part in row 1, column 2]

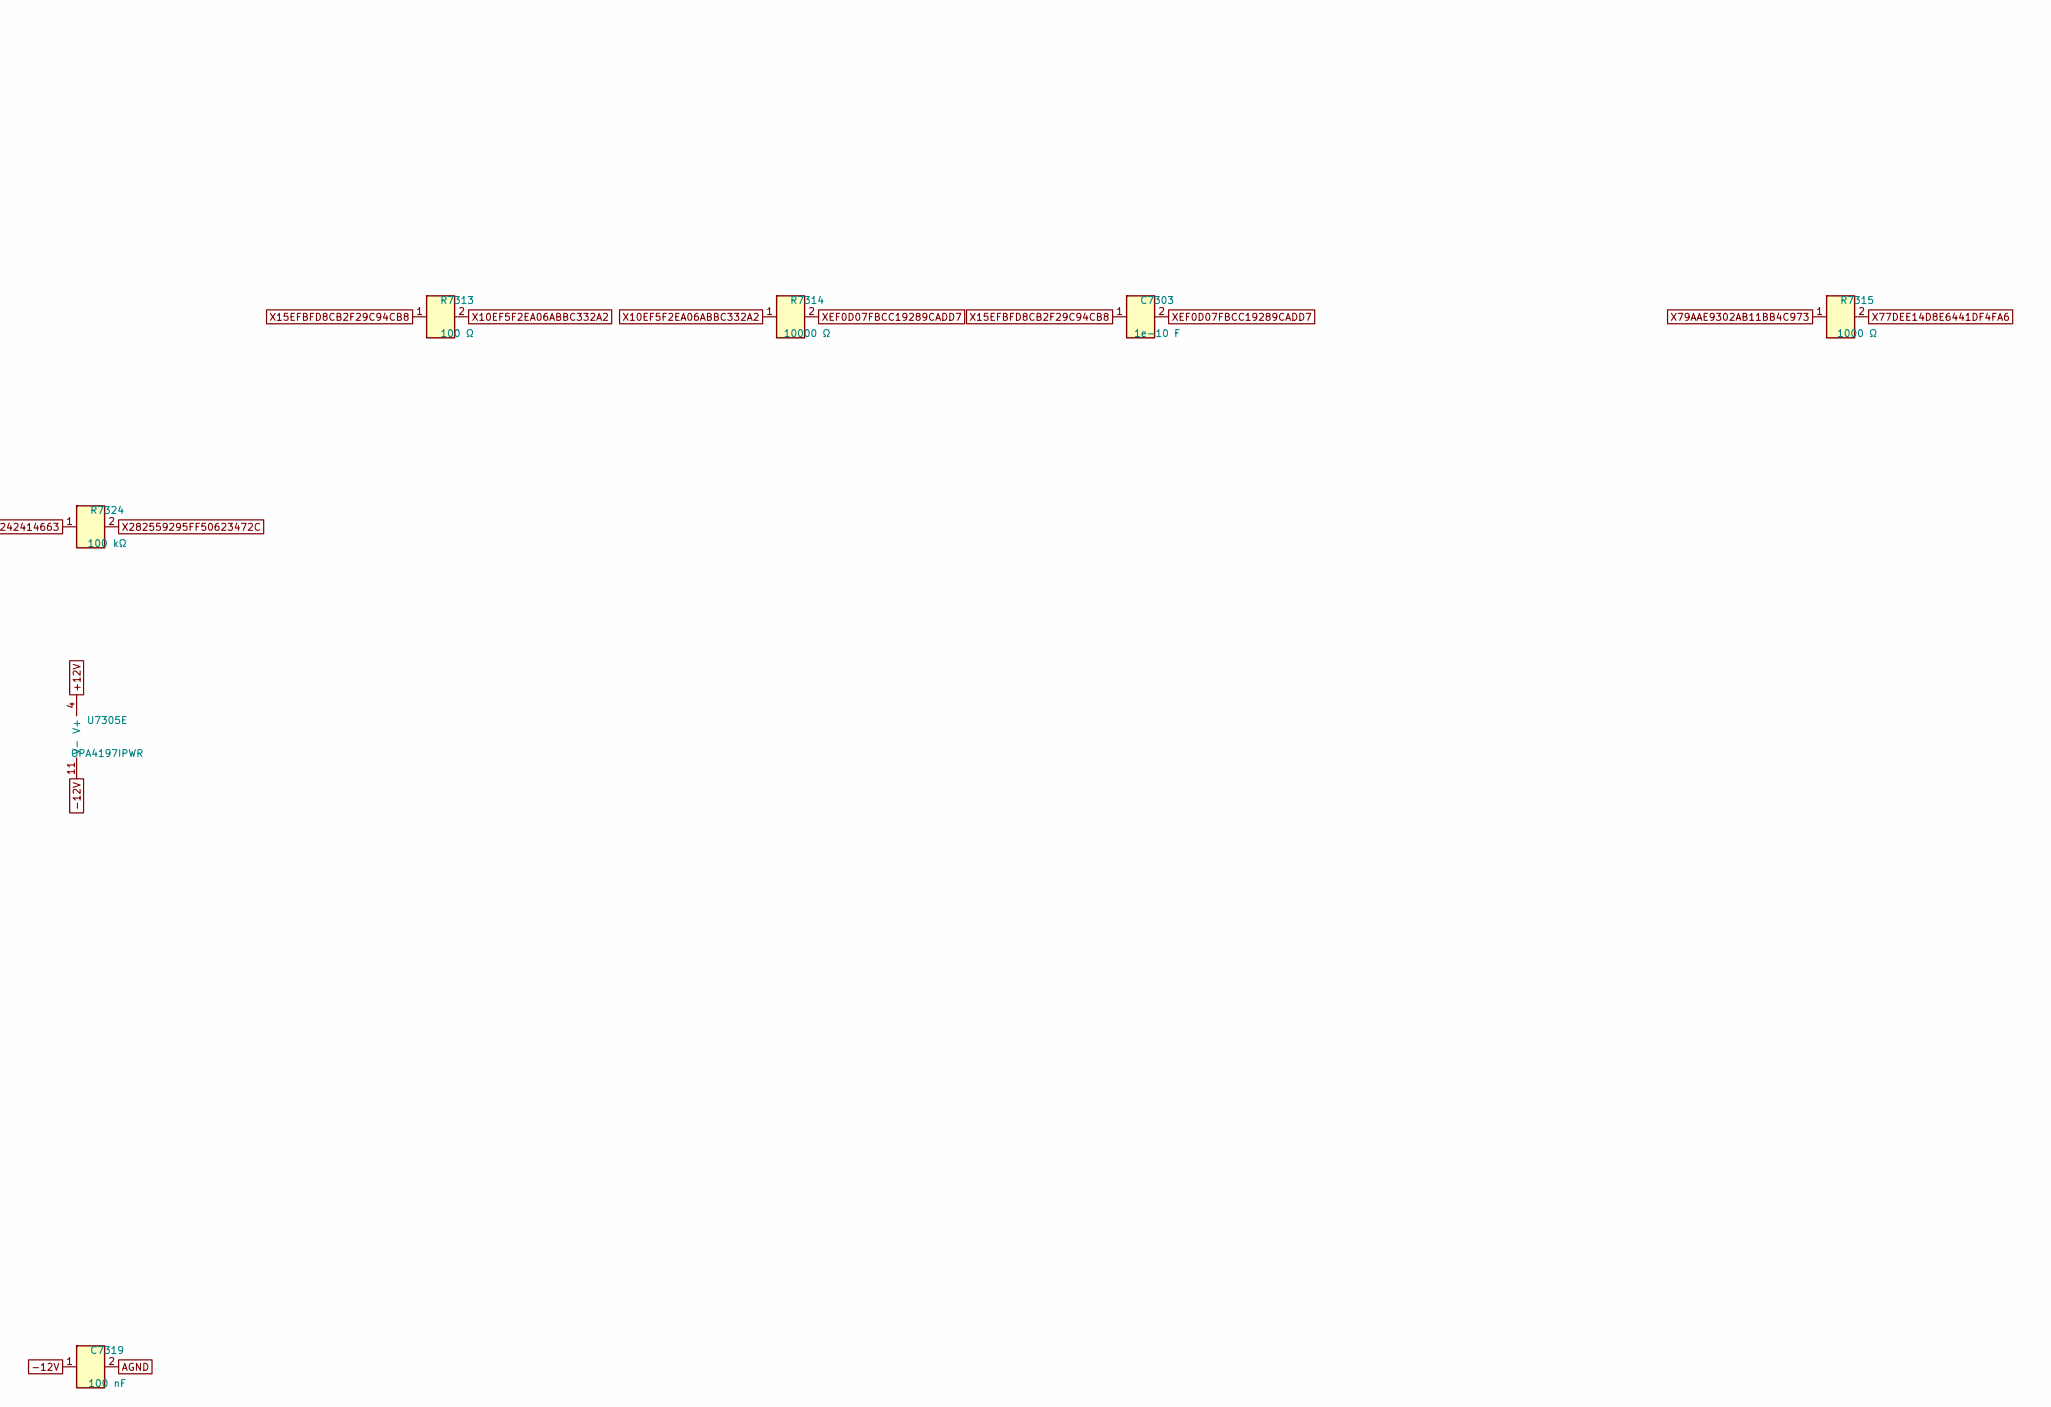
[picture p169: schematic offset_A03_K.kicad_sch, part in row 1, column 3]

Parts:
C7301: 1e-07 F; C0603; MPN GRM188R71H104KA93D
C7302: 1e-06 F; C0603
C7303: 1e-10 F; C0603; MPN C0603C101J5GACTU
C7304: 1e-11 F; C0603
C7305: 1e-08 F; C0603
C7307, C7316, C7317, C7318, C7319: 100 nF; C0603; MPN GRM188R71H104KA93D
R7301, R7302, R7314: 10000 Ω; R0603
R7303: 22000 Ω; R0603
R7304, R7317, R7318: 100000 Ω; R0603; MPN RT0603BRD07100KL
R7313: 100 Ω; R0603
R7315, R7319: 1000 Ω; R0603
R7316, R7320: 1e+07 Ω; R0603
R7321, R7322, R7323, R7324: 100 kΩ; R0603; MPN RT0603BRD07100KL
U7301: REF5050AIDR; SOIC-8_3.9x4.9mm_P1.27mm; MPN REF5050AIDR; LCSC C27804
U7304, U7305: OPA4197IPWR; TSSOP-14_4.4x5mm_P0.65mm; MPN OPA4197IPWR; LCSC C2057327

Connections:
+12V: C7301.1, C7307.1, C7316.1, C7318.1, U7301.2 (Vin), U7304.4 (V+), U7305.4 (V+)
-12V: C7317.1, C7319.1, U7304.11 (V-), U7305.11 (V-)
AGND: C7301.2, C7302.2, C7305.2, C7307.2, C7316.2, C7317.2, C7318.2, C7319.2, R7304.2, R7316.2, R7320.2, U7301.4 (GND), U7304.5 (+), U7305.10 (+), U7305.12 (+)
X0FD413992017D867ECC2: C7305.1, R7319.2, R7320.1, U7305.5 (+)
X1E1299B7B09613B0B0D3: R7317.1, U7304.12 (+)
X4AC9B2A2F3AAE64DF11E: U7305.13 (-), U7305.14
X6C62630F9BE0A61B41E6: R7322.1, U7305.6 (-), U7305.7
X10EF5F2EA06ABBC332A2: R7313.2, R7314.1
X15EFBFD8CB2F29C94CB8: C7303.1, R7313.1, U7304.14
X31AD357F953533228F7F: U7304.8, U7304.9 (-)
X73B2519EBEC246C65607: R7323.1
X77DEE14D8E6441DF4FA6: R7315.2, R7316.1, U7305.3 (+)
X79AAE9302AB11BB4C973: R7315.1
X095C3880B748D77B193B: C7304.1, R7318.1, R7321.1, U7305.1
X05736A904C0279F1CE63: R7302.1, U7304.7
X223634D8F0FE443723F0: R7303.2, R7304.1, U7304.10 (+)
X282559295FF50623472C: R7321.2, R7322.2, R7323.2, R7324.2, U7305.9 (-)
XBA90FAD9780242414663: R7324.1, U7305.8
XD6E82A5ACAA8A64577A5: C7302.1, U7301.6 (Vout), U7304.3 (+)
XD9C40D9D9661328B6EFF: R7301.2, R7302.2, U7304.6 (-)
XE2B9B937D5CAF54AD63F: R7301.1, R7303.1, U7304.1, U7304.2 (-)
XEEF5A855E362B4B0F6B0: R7319.1
XEF0D07FBCC19289CADD7: C7303.2, R7314.2, U7304.13 (-)
XF5F99B56C65F641EF950: C7304.2, R7317.2, R7318.2, U7305.2 (-)
