Takazudo/zudo-osc-hole-field/boards/osc-core/sheets/offset_A04_K.kicad_sch

## KiCad design boards/osc-core/sheets/offset_A04_K.kicad_sch (2026-10-05)

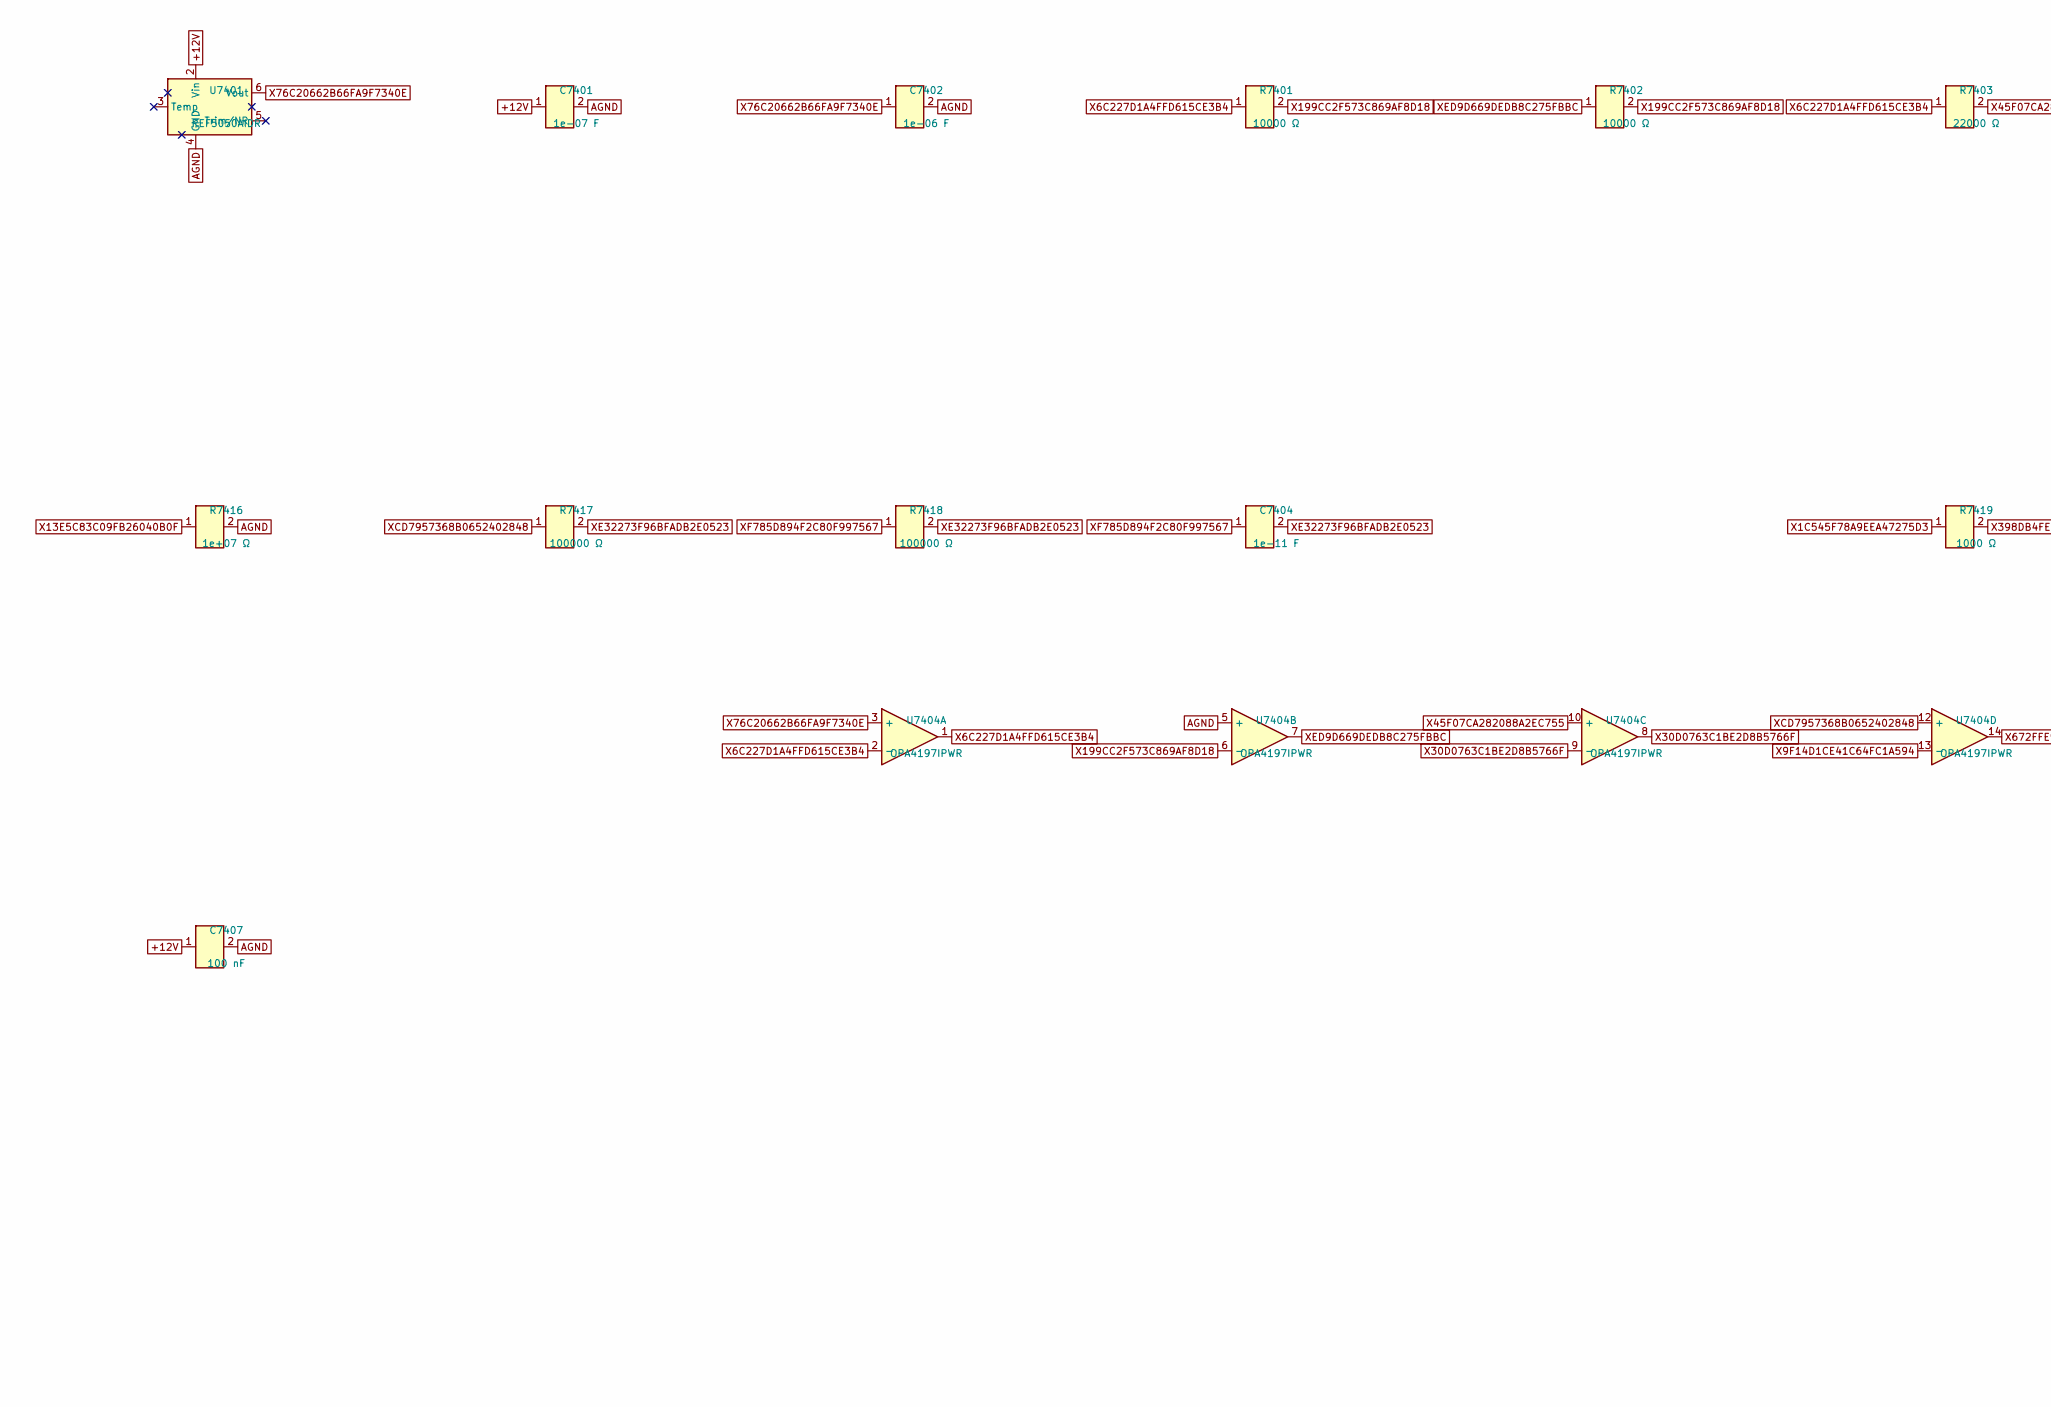
[picture p170: schematic offset_A04_K.kicad_sch, part in row 1, column 1]

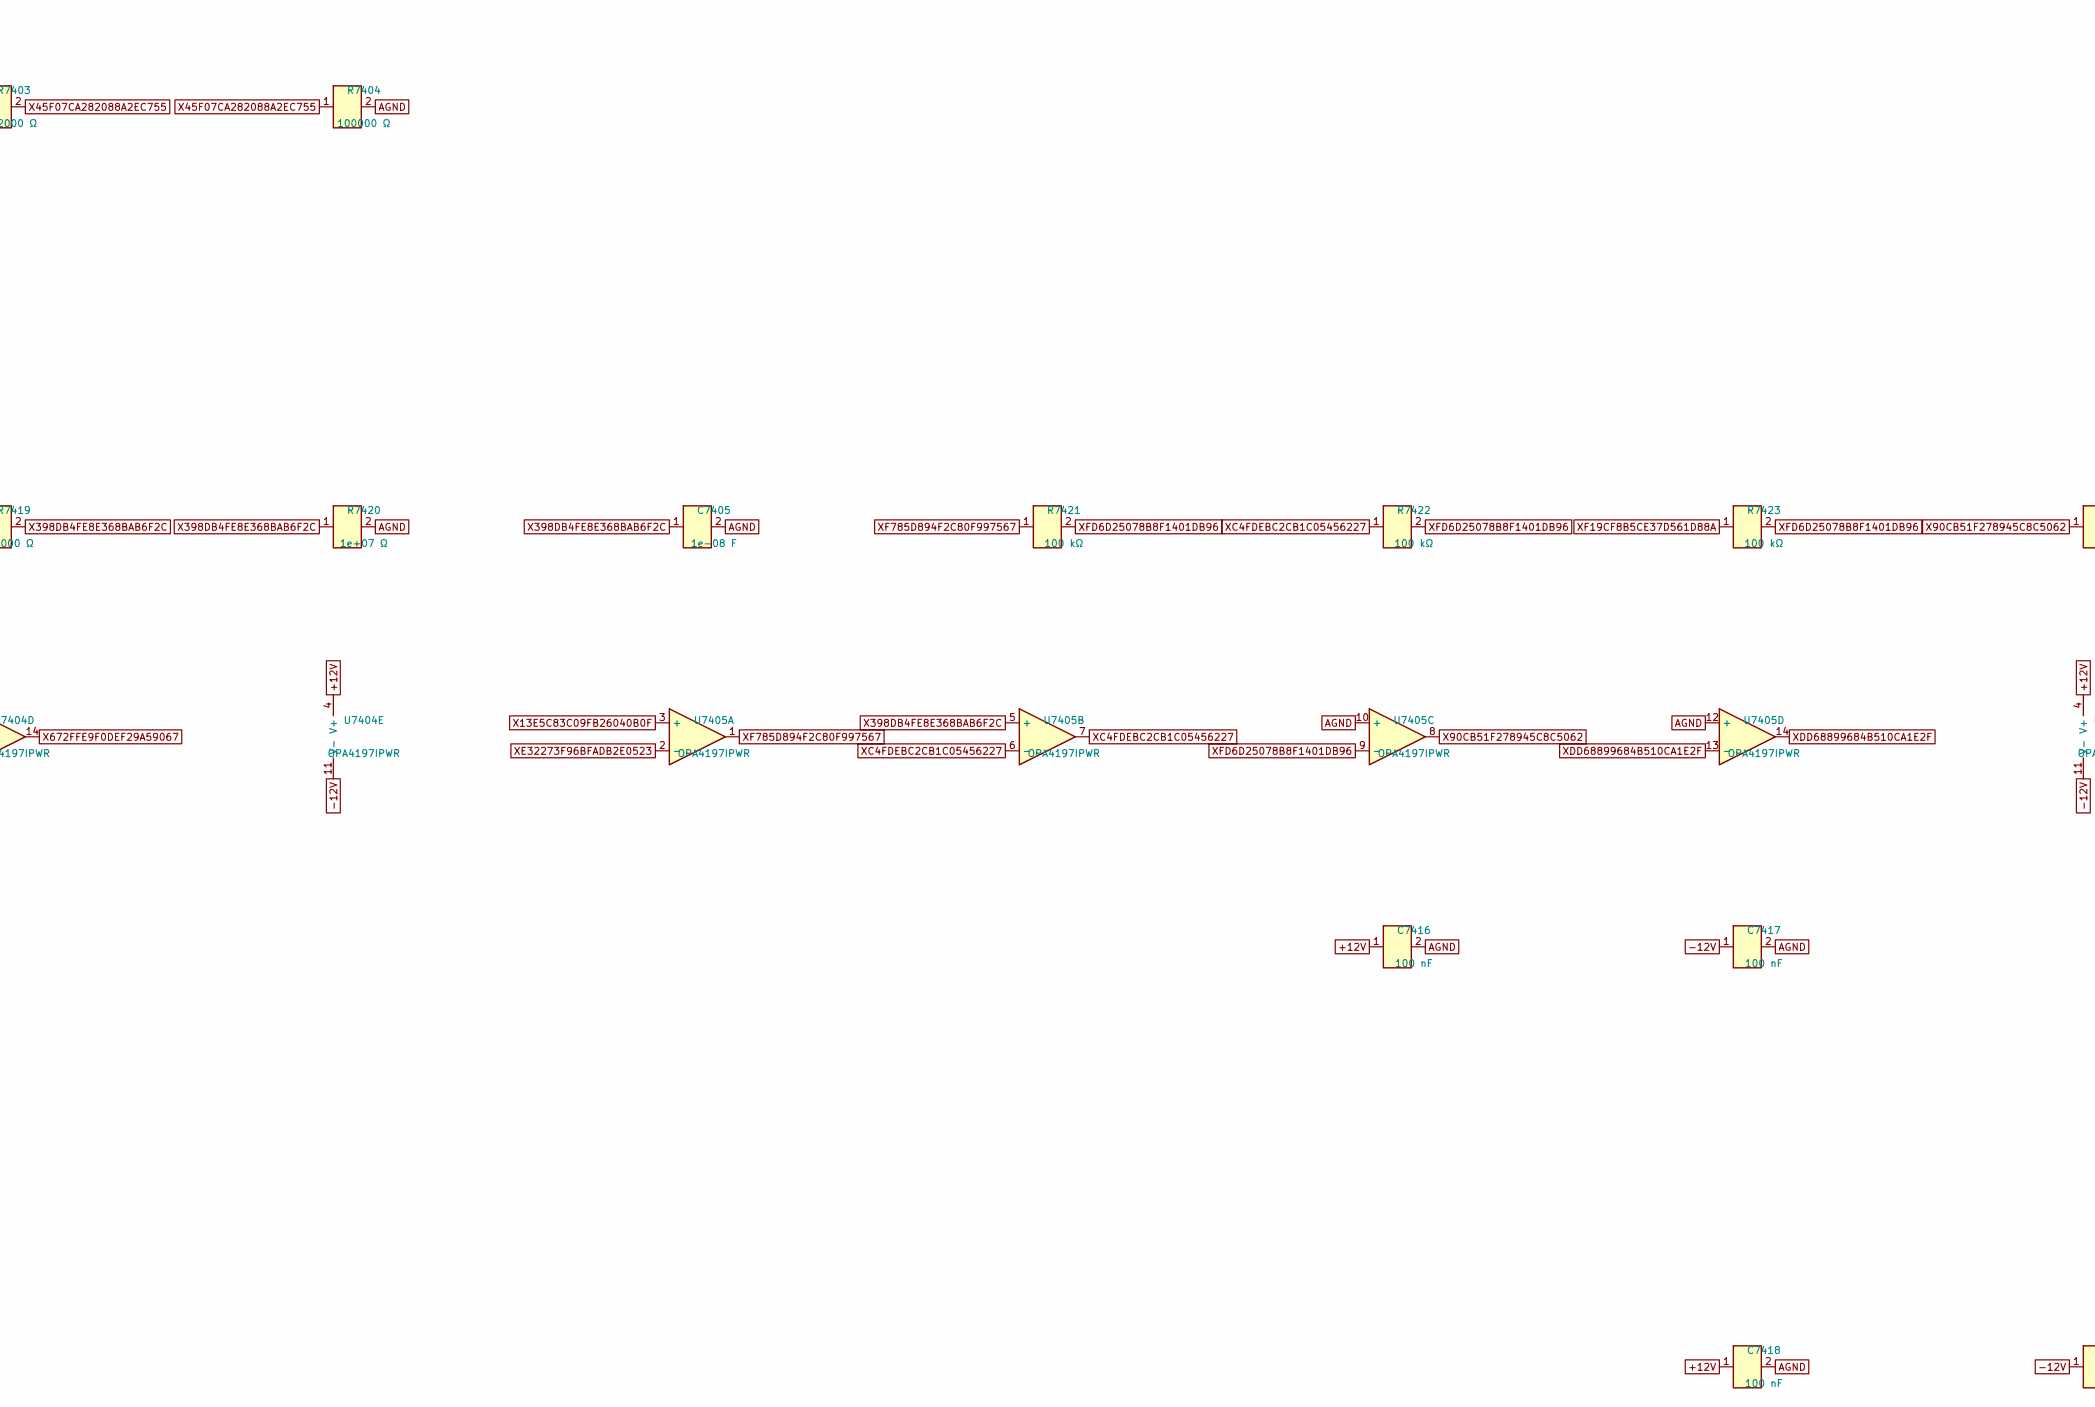
[picture p171: schematic offset_A04_K.kicad_sch, part in row 1, column 2]

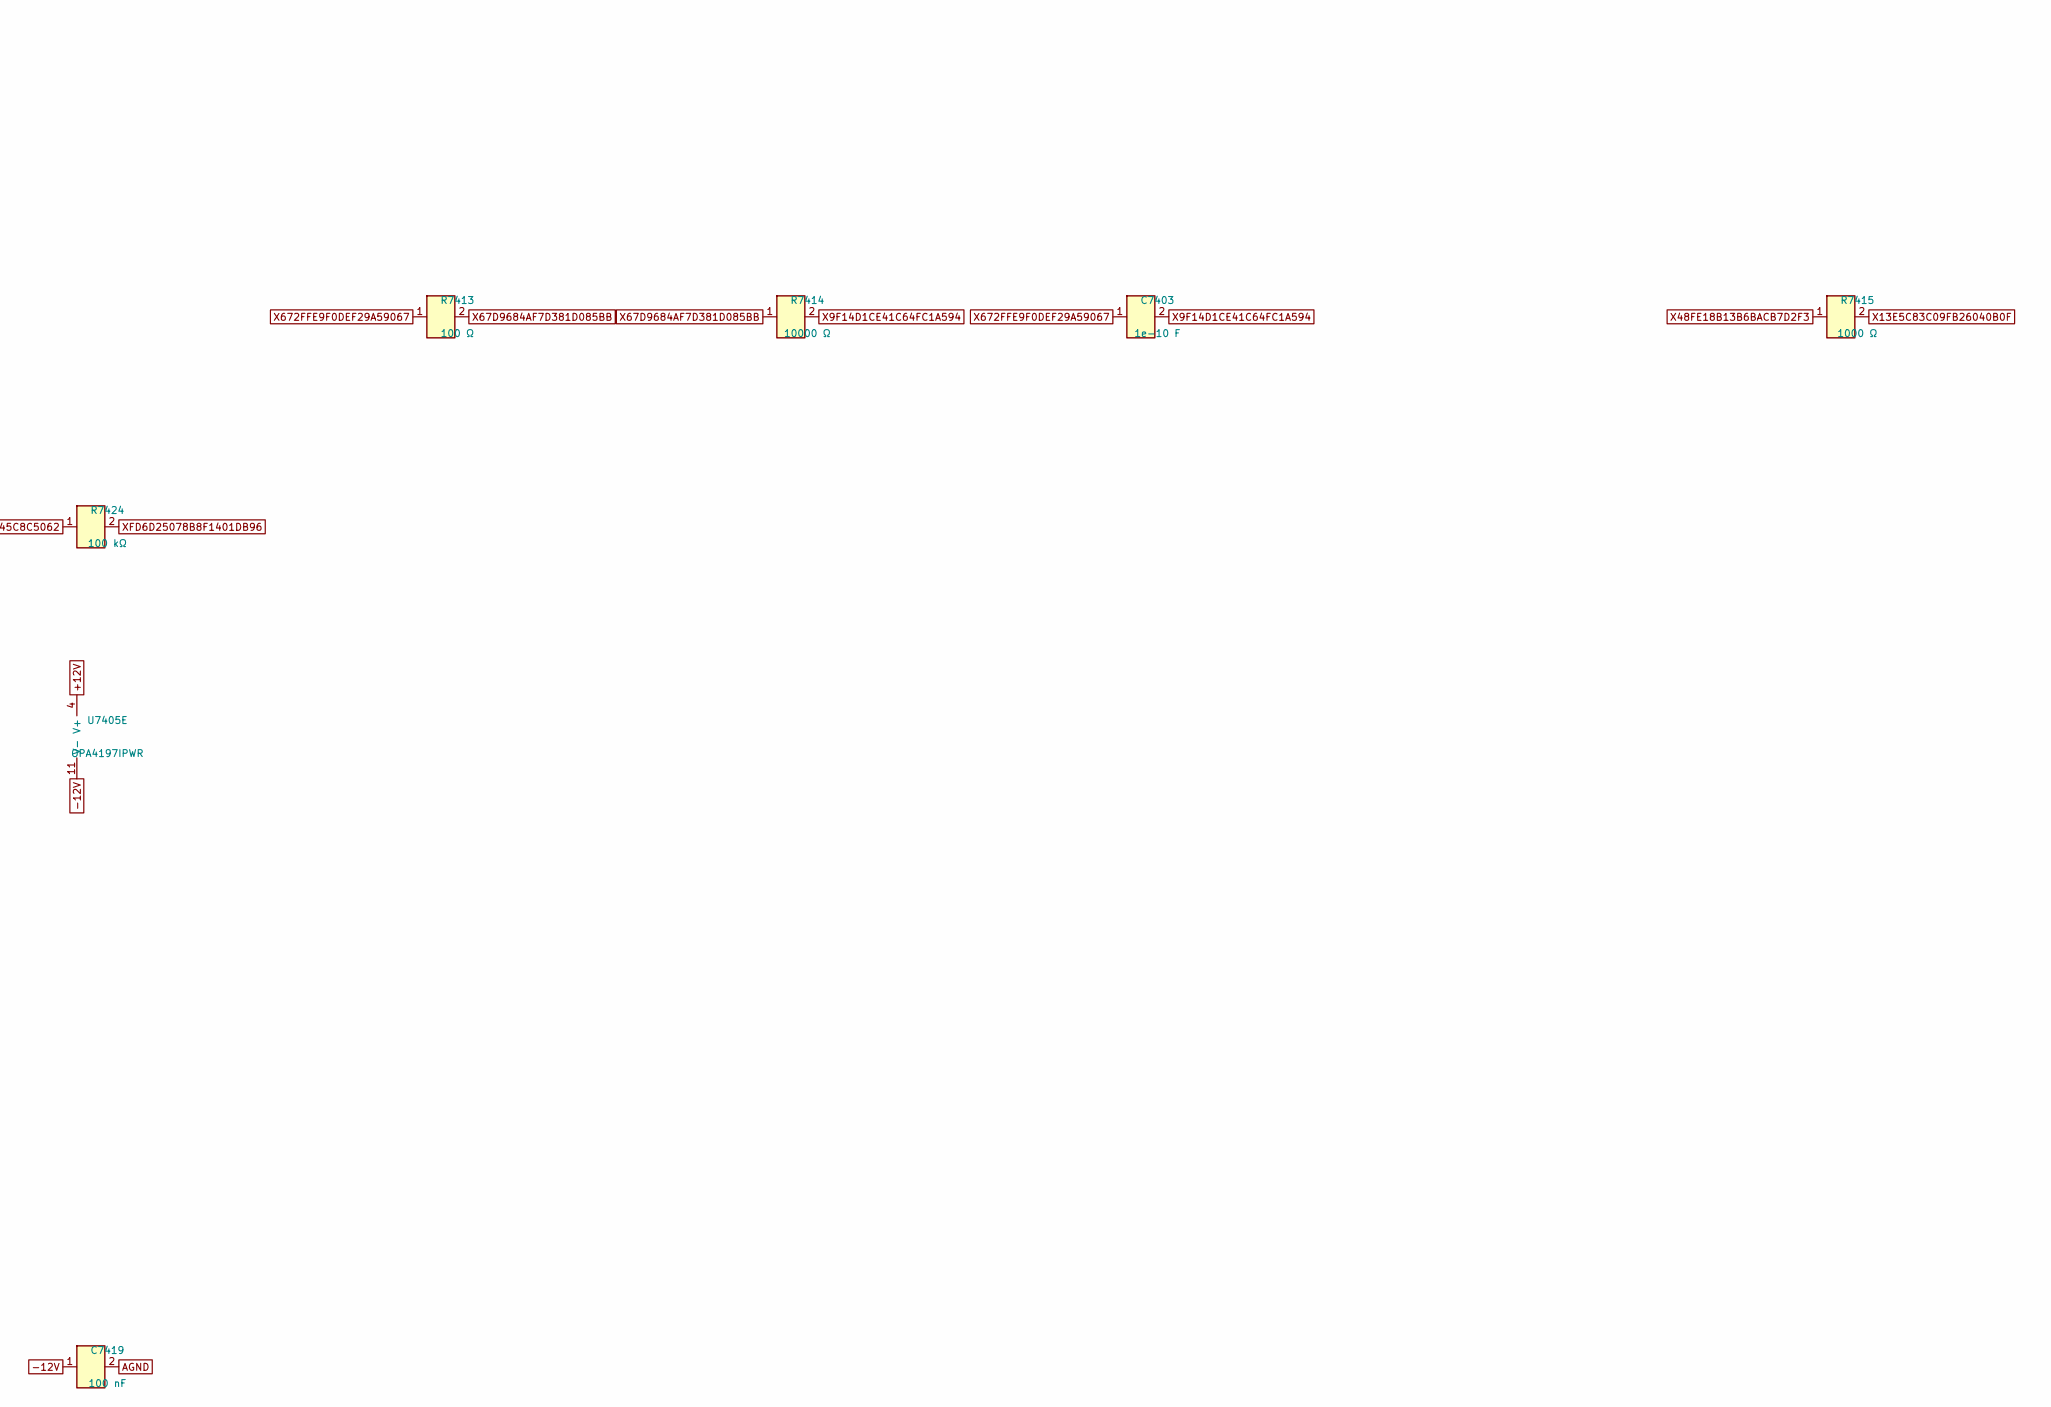
[picture p172: schematic offset_A04_K.kicad_sch, part in row 1, column 3]

Parts:
C7401: 1e-07 F; C0603; MPN GRM188R71H104KA93D
C7402: 1e-06 F; C0603
C7403: 1e-10 F; C0603; MPN C0603C101J5GACTU
C7404: 1e-11 F; C0603
C7405: 1e-08 F; C0603
C7407, C7416, C7417, C7418, C7419: 100 nF; C0603; MPN GRM188R71H104KA93D
R7401, R7402, R7414: 10000 Ω; R0603
R7403: 22000 Ω; R0603
R7404, R7417, R7418: 100000 Ω; R0603; MPN RT0603BRD07100KL
R7413: 100 Ω; R0603
R7415, R7419: 1000 Ω; R0603
R7416, R7420: 1e+07 Ω; R0603
R7421, R7422, R7423, R7424: 100 kΩ; R0603; MPN RT0603BRD07100KL
U7401: REF5050AIDR; SOIC-8_3.9x4.9mm_P1.27mm; MPN REF5050AIDR; LCSC C27804
U7404, U7405: OPA4197IPWR; TSSOP-14_4.4x5mm_P0.65mm; MPN OPA4197IPWR; LCSC C2057327

Connections:
+12V: C7401.1, C7407.1, C7416.1, C7418.1, U7401.2 (Vin), U7404.4 (V+), U7405.4 (V+)
-12V: C7417.1, C7419.1, U7404.11 (V-), U7405.11 (V-)
AGND: C7401.2, C7402.2, C7405.2, C7407.2, C7416.2, C7417.2, C7418.2, C7419.2, R7404.2, R7416.2, R7420.2, U7401.4 (GND), U7404.5 (+), U7405.10 (+), U7405.12 (+)
X1C545F78A9EEA47275D3: R7419.1
X6C227D1A4FFD615CE3B4: R7401.1, R7403.1, U7404.1, U7404.2 (-)
X9F14D1CE41C64FC1A594: C7403.2, R7414.2, U7404.13 (-)
X13E5C83C09FB26040B0F: R7415.2, R7416.1, U7405.3 (+)
X30D0763C1BE2D8B5766F: U7404.8, U7404.9 (-)
X45F07CA282088A2EC755: R7403.2, R7404.1, U7404.10 (+)
X48FE18B13B6BACB7D2F3: R7415.1
X67D9684AF7D381D085BB: R7413.2, R7414.1
X76C20662B66FA9F7340E: C7402.1, U7401.6 (Vout), U7404.3 (+)
X90CB51F278945C8C5062: R7424.1, U7405.8
X199CC2F573C869AF8D18: R7401.2, R7402.2, U7404.6 (-)
X398DB4FE8E368BAB6F2C: C7405.1, R7419.2, R7420.1, U7405.5 (+)
X672FFE9F0DEF29A59067: C7403.1, R7413.1, U7404.14
XC4FDEBC2CB1C05456227: R7422.1, U7405.6 (-), U7405.7
XCD7957368B0652402848: R7417.1, U7404.12 (+)
XDD68899684B510CA1E2F: U7405.13 (-), U7405.14
XE32273F96BFADB2E0523: C7404.2, R7417.2, R7418.2, U7405.2 (-)
XED9D669DEDB8C275FBBC: R7402.1, U7404.7
XF19CF8B5CE37D561D88A: R7423.1
XF785D894F2C80F997567: C7404.1, R7418.1, R7421.1, U7405.1
XFD6D25078B8F1401DB96: R7421.2, R7422.2, R7423.2, R7424.2, U7405.9 (-)
