Takazudo/zudo-osc-hole-field/boards/osc-core/sheets/offset_A05_K.kicad_sch

## KiCad design boards/osc-core/sheets/offset_A05_K.kicad_sch (2026-10-05)

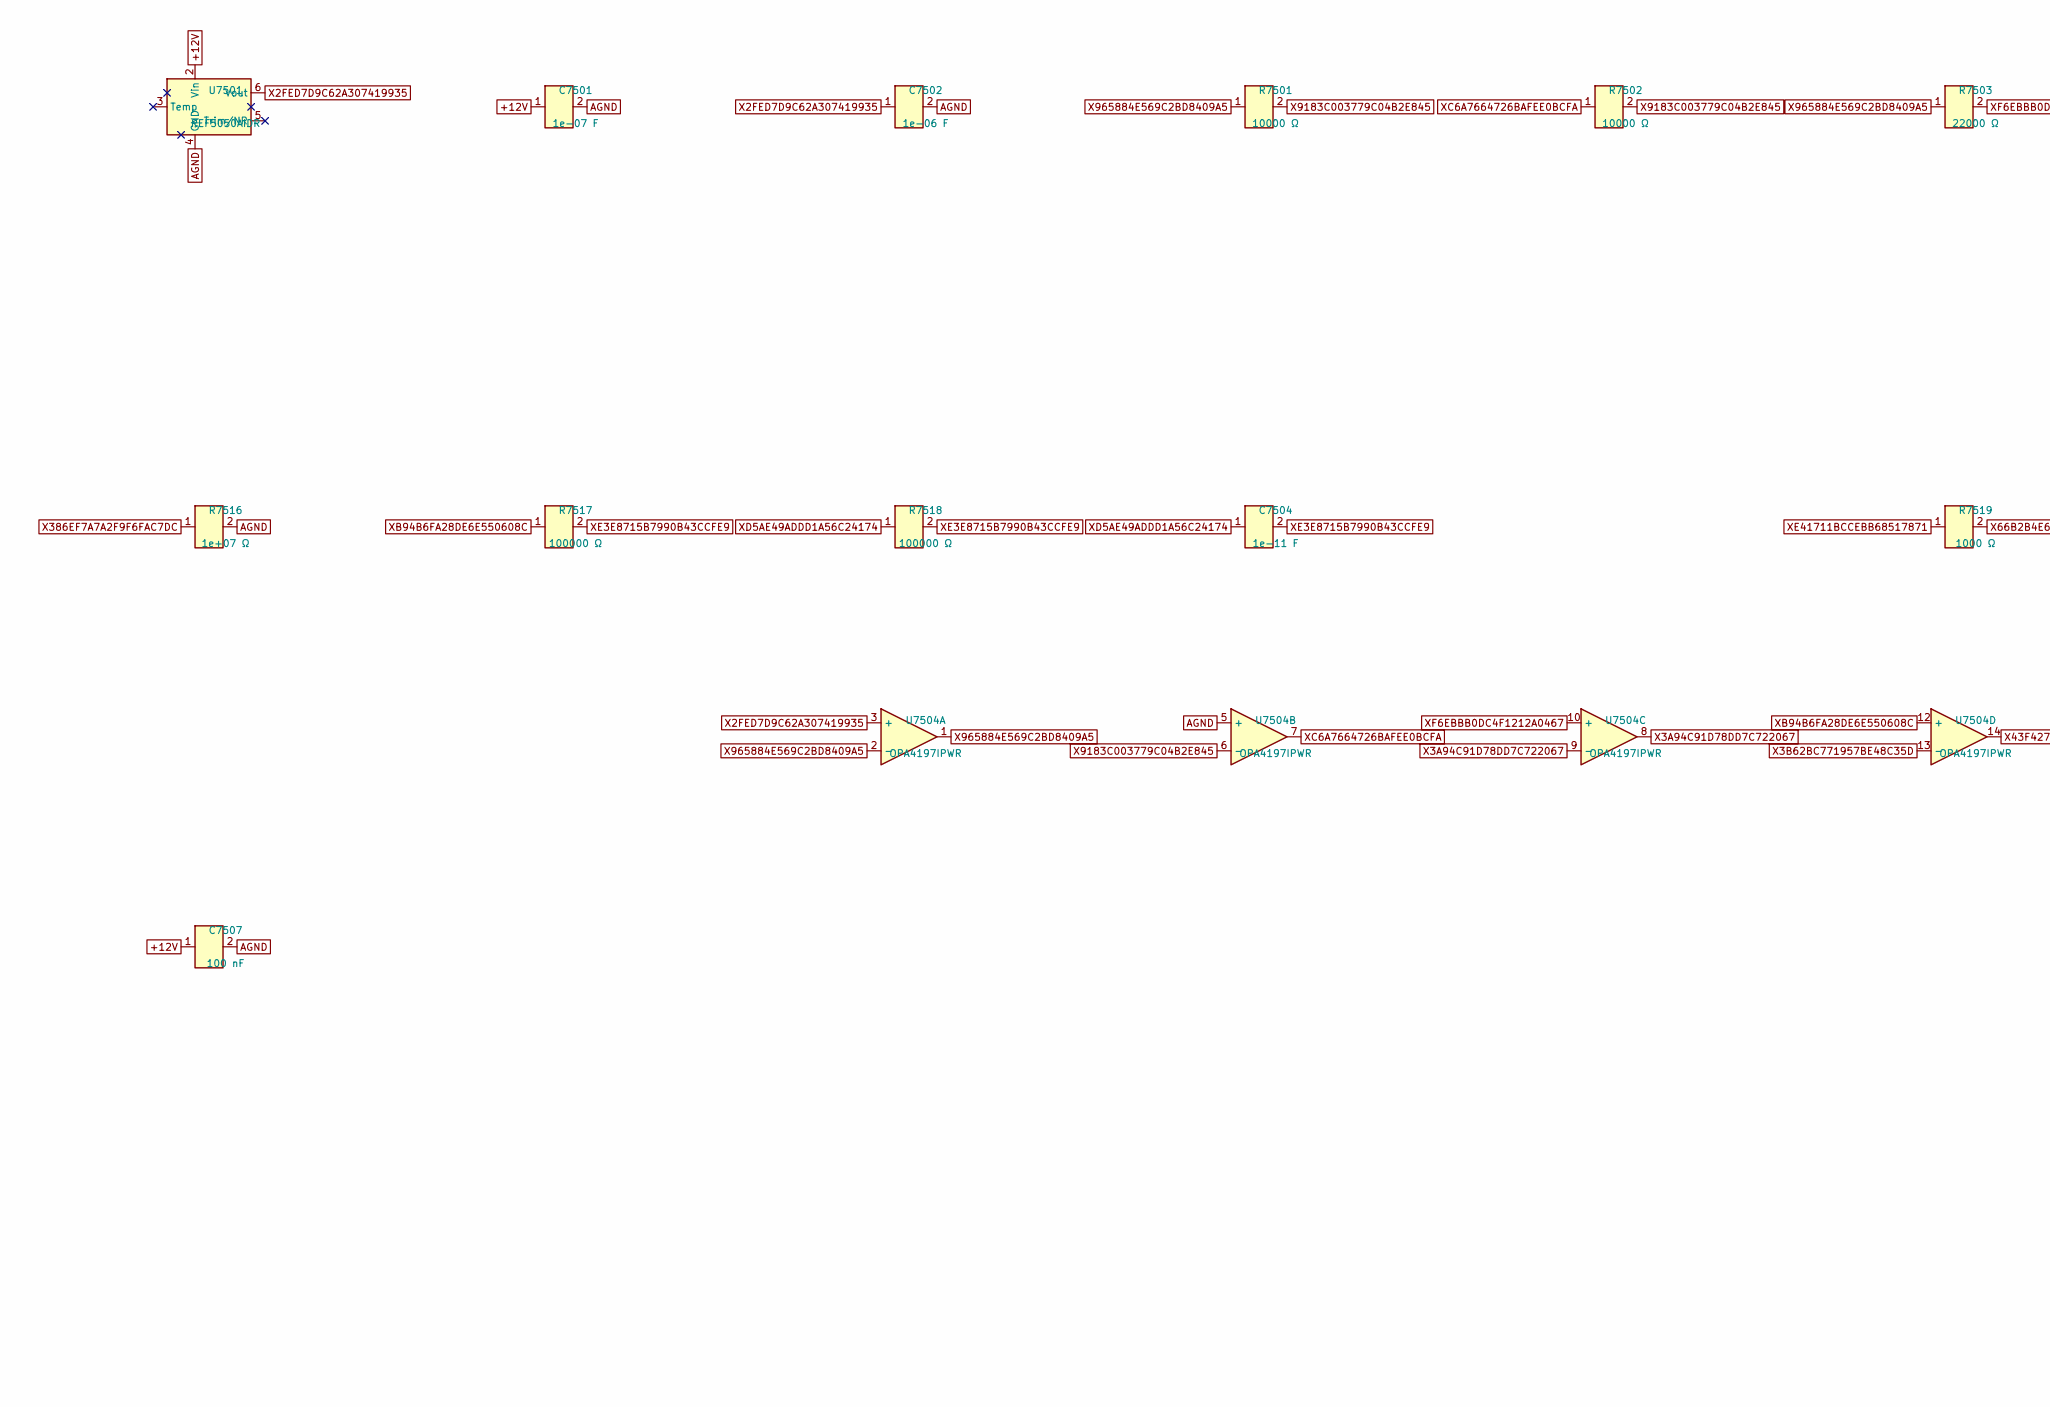
[picture p173: schematic offset_A05_K.kicad_sch, part in row 1, column 1]

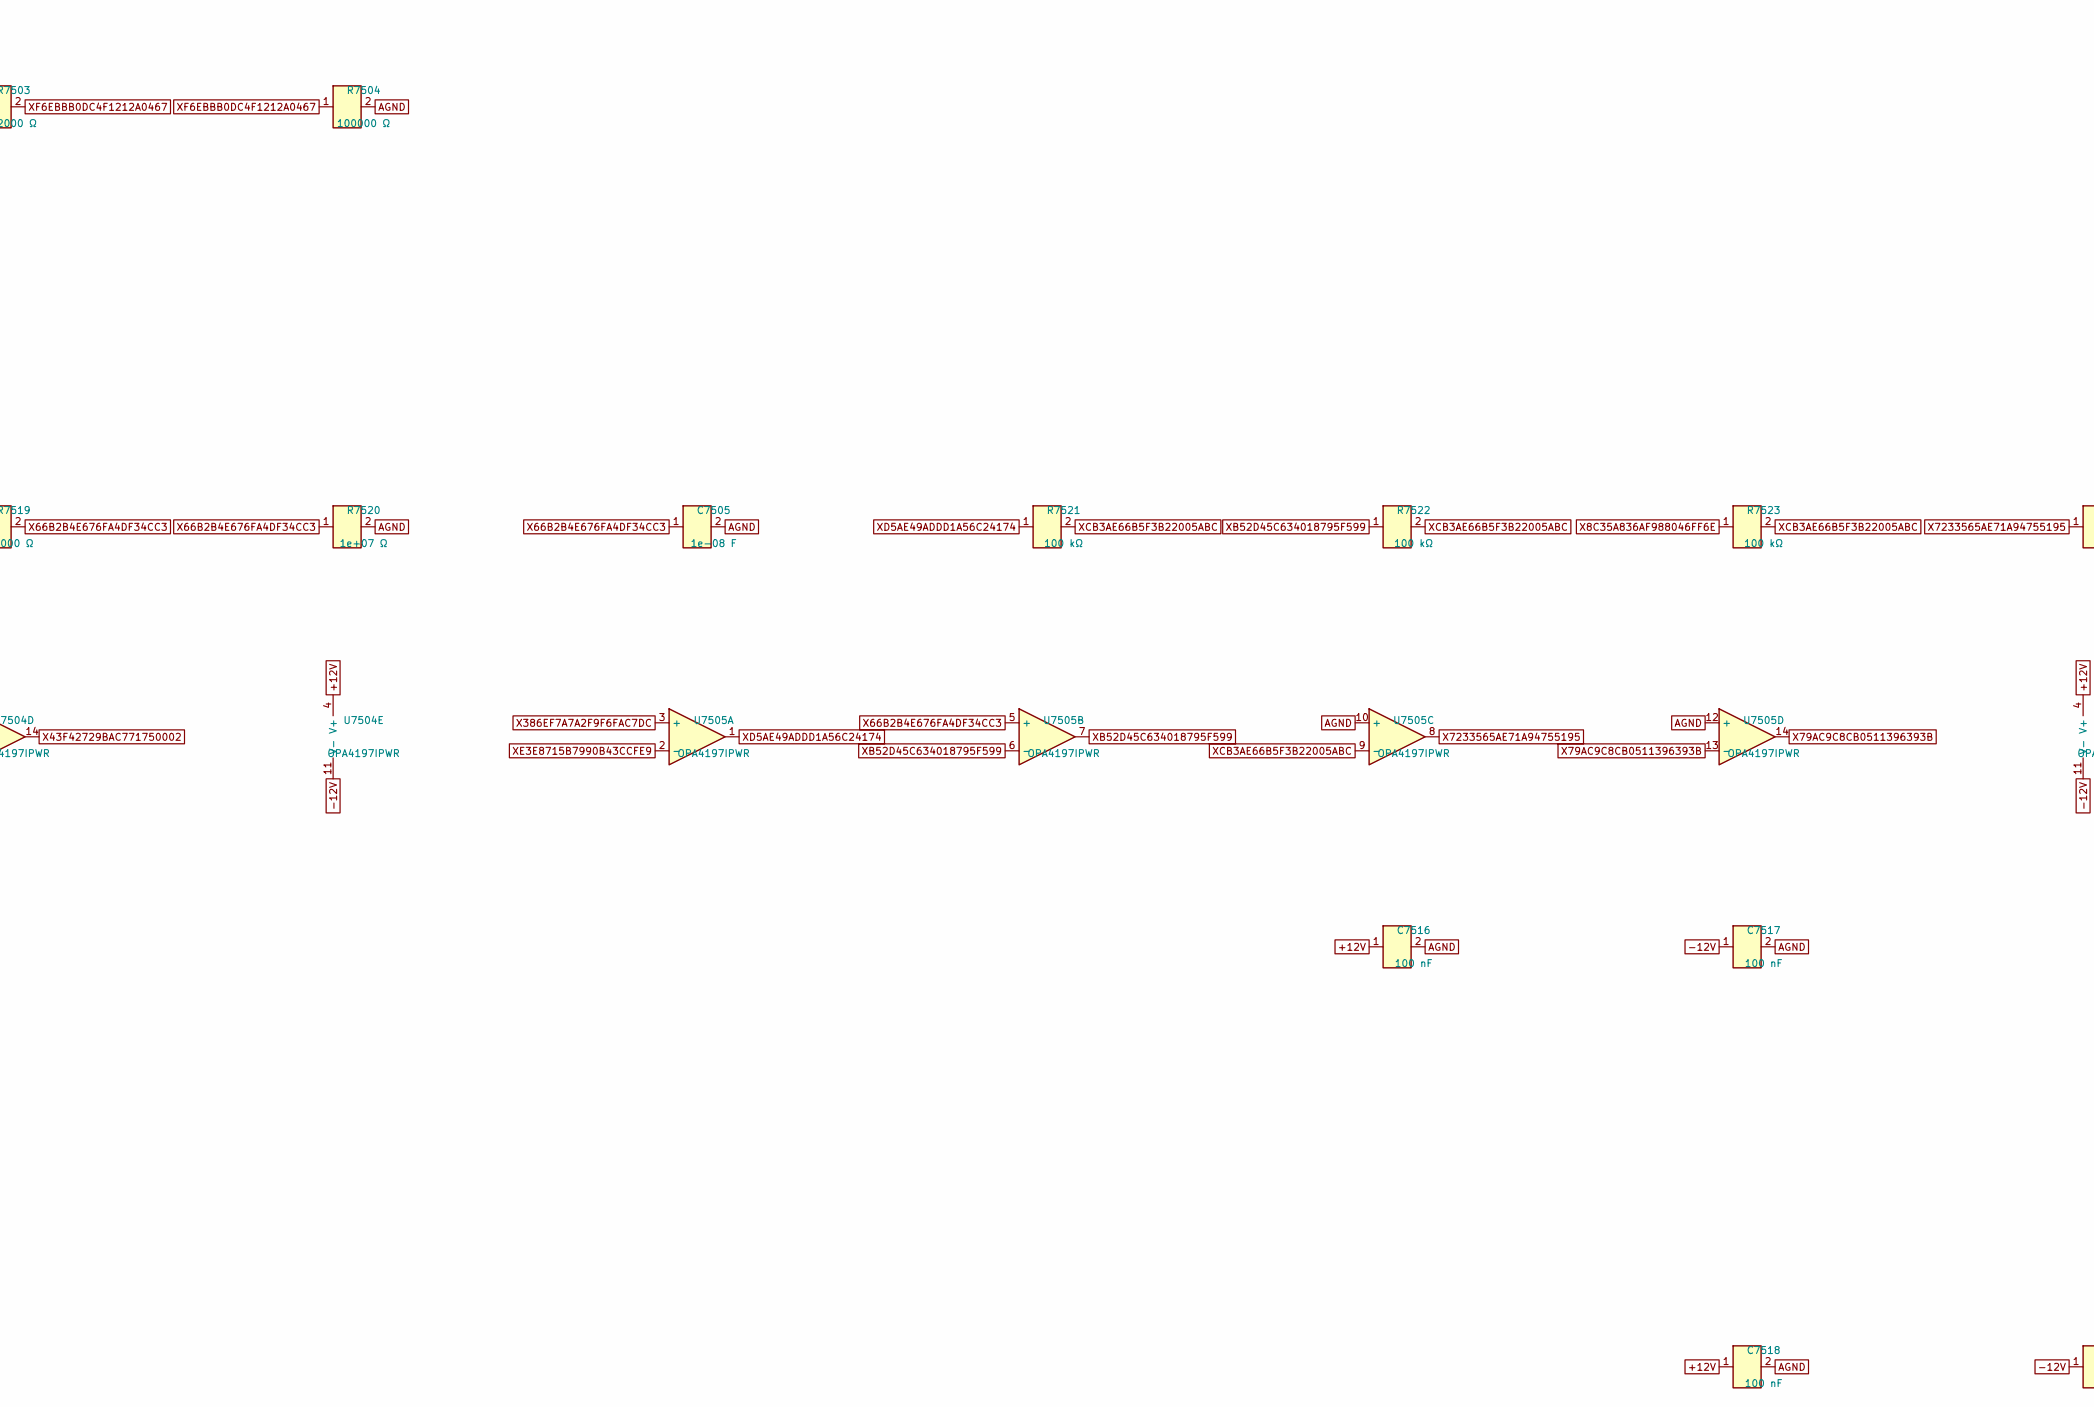
[picture p174: schematic offset_A05_K.kicad_sch, part in row 1, column 2]

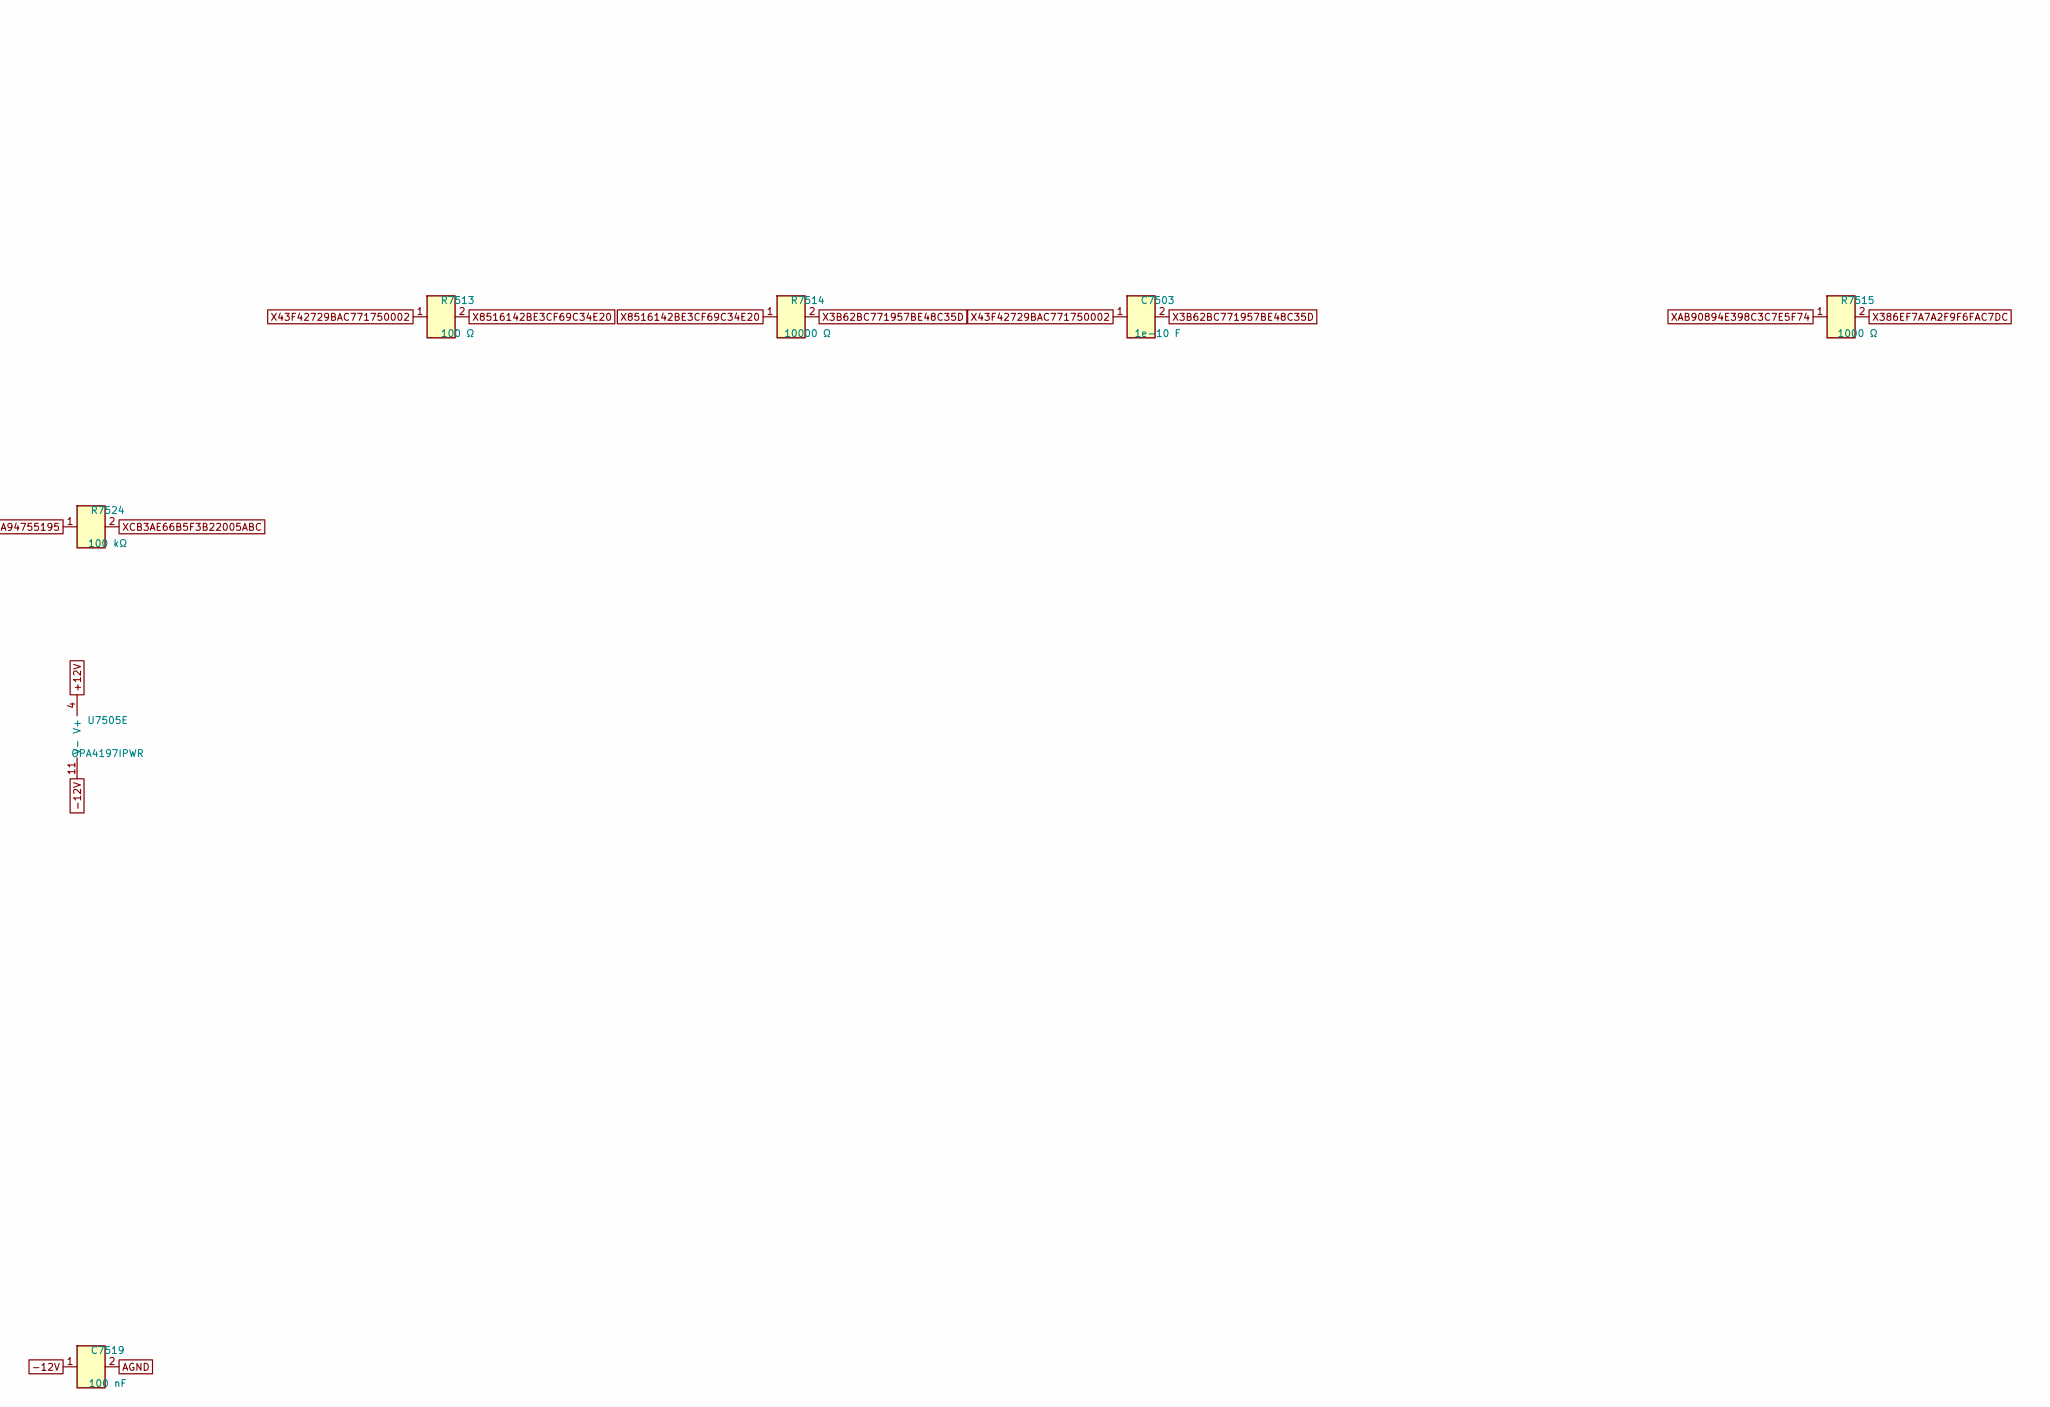
[picture p175: schematic offset_A05_K.kicad_sch, part in row 1, column 3]

Parts:
C7501: 1e-07 F; C0603; MPN GRM188R71H104KA93D
C7502: 1e-06 F; C0603
C7503: 1e-10 F; C0603; MPN C0603C101J5GACTU
C7504: 1e-11 F; C0603
C7505: 1e-08 F; C0603
C7507, C7516, C7517, C7518, C7519: 100 nF; C0603; MPN GRM188R71H104KA93D
R7501, R7502, R7514: 10000 Ω; R0603
R7503: 22000 Ω; R0603
R7504, R7517, R7518: 100000 Ω; R0603; MPN RT0603BRD07100KL
R7513: 100 Ω; R0603
R7515, R7519: 1000 Ω; R0603
R7516, R7520: 1e+07 Ω; R0603
R7521, R7522, R7523, R7524: 100 kΩ; R0603; MPN RT0603BRD07100KL
U7501: REF5050AIDR; SOIC-8_3.9x4.9mm_P1.27mm; MPN REF5050AIDR; LCSC C27804
U7504, U7505: OPA4197IPWR; TSSOP-14_4.4x5mm_P0.65mm; MPN OPA4197IPWR; LCSC C2057327

Connections:
+12V: C7501.1, C7507.1, C7516.1, C7518.1, U7501.2 (Vin), U7504.4 (V+), U7505.4 (V+)
-12V: C7517.1, C7519.1, U7504.11 (V-), U7505.11 (V-)
AGND: C7501.2, C7502.2, C7505.2, C7507.2, C7516.2, C7517.2, C7518.2, C7519.2, R7504.2, R7516.2, R7520.2, U7501.4 (GND), U7504.5 (+), U7505.10 (+), U7505.12 (+)
X2FED7D9C62A307419935: C7502.1, U7501.6 (Vout), U7504.3 (+)
X3A94C91D78DD7C722067: U7504.8, U7504.9 (-)
X3B62BC771957BE48C35D: C7503.2, R7514.2, U7504.13 (-)
X8C35A836AF988046FF6E: R7523.1
X43F42729BAC771750002: C7503.1, R7513.1, U7504.14
X66B2B4E676FA4DF34CC3: C7505.1, R7519.2, R7520.1, U7505.5 (+)
X79AC9C8CB0511396393B: U7505.13 (-), U7505.14
X386EF7A7A2F9F6FAC7DC: R7515.2, R7516.1, U7505.3 (+)
X9183C003779C04B2E845: R7501.2, R7502.2, U7504.6 (-)
X965884E569C2BD8409A5: R7501.1, R7503.1, U7504.1, U7504.2 (-)
X7233565AE71A94755195: R7524.1, U7505.8
X8516142BE3CF69C34E20: R7513.2, R7514.1
XAB90894E398C3C7E5F74: R7515.1
XB52D45C634018795F599: R7522.1, U7505.6 (-), U7505.7
XB94B6FA28DE6E550608C: R7517.1, U7504.12 (+)
XC6A7664726BAFEE0BCFA: R7502.1, U7504.7
XCB3AE66B5F3B22005ABC: R7521.2, R7522.2, R7523.2, R7524.2, U7505.9 (-)
XD5AE49ADDD1A56C24174: C7504.1, R7518.1, R7521.1, U7505.1
XE3E8715B7990B43CCFE9: C7504.2, R7517.2, R7518.2, U7505.2 (-)
XE41711BCCEBB68517871: R7519.1
XF6EBBB0DC4F1212A0467: R7503.2, R7504.1, U7504.10 (+)
