Takazudo/zudo-osc-hole-field/boards/osc-core/sheets/offset_A06_K.kicad_sch

## KiCad design boards/osc-core/sheets/offset_A06_K.kicad_sch (2026-10-05)

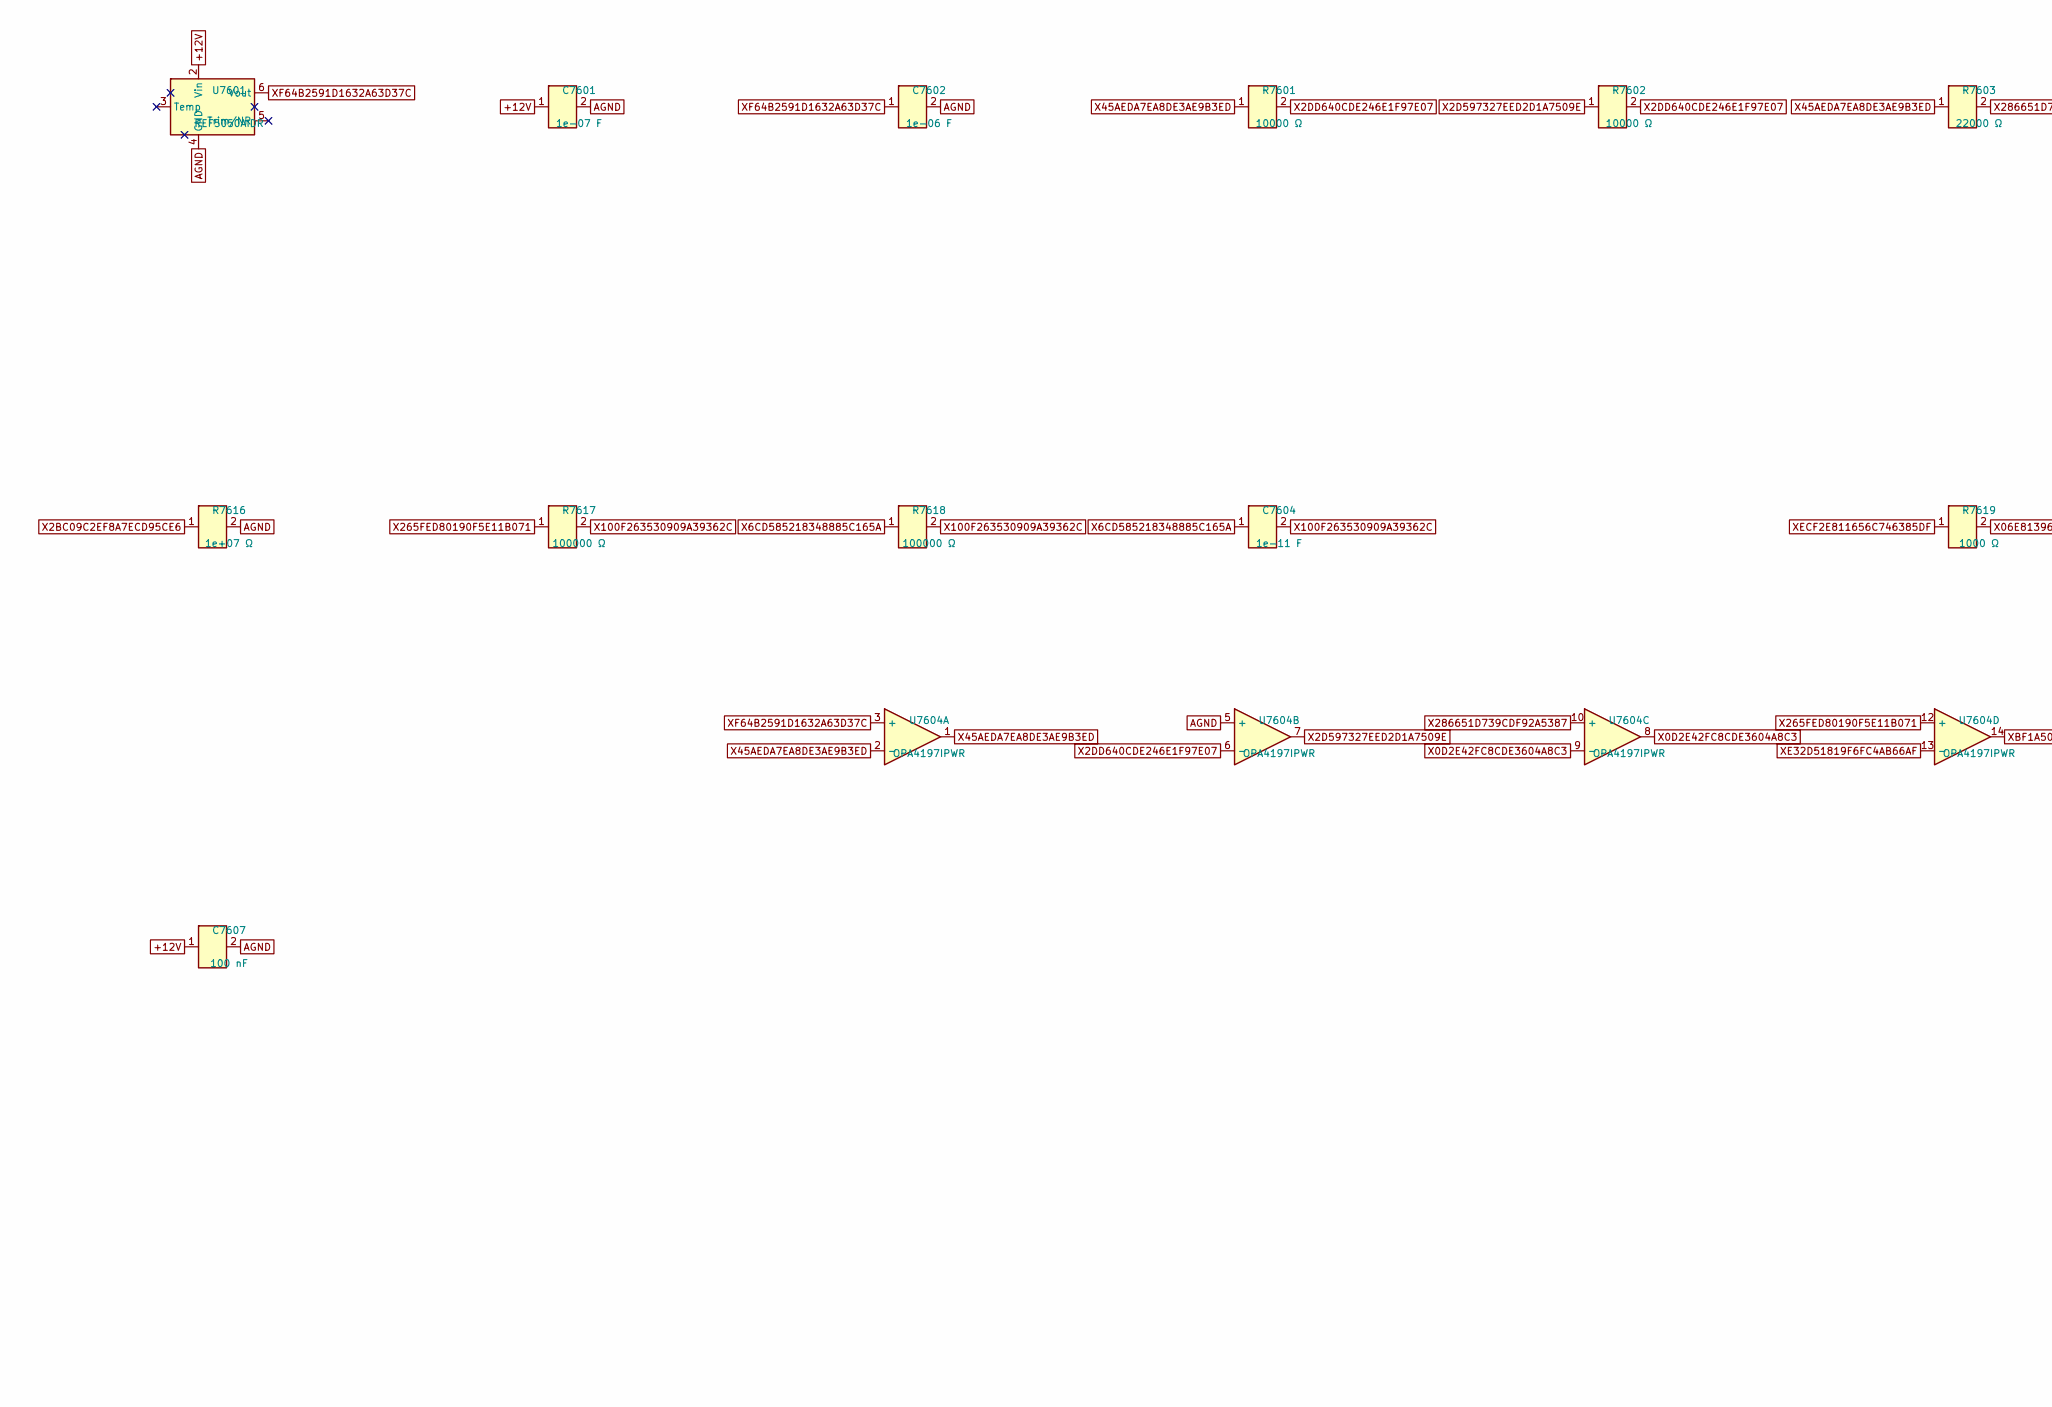
[picture p176: schematic offset_A06_K.kicad_sch, part in row 1, column 1]

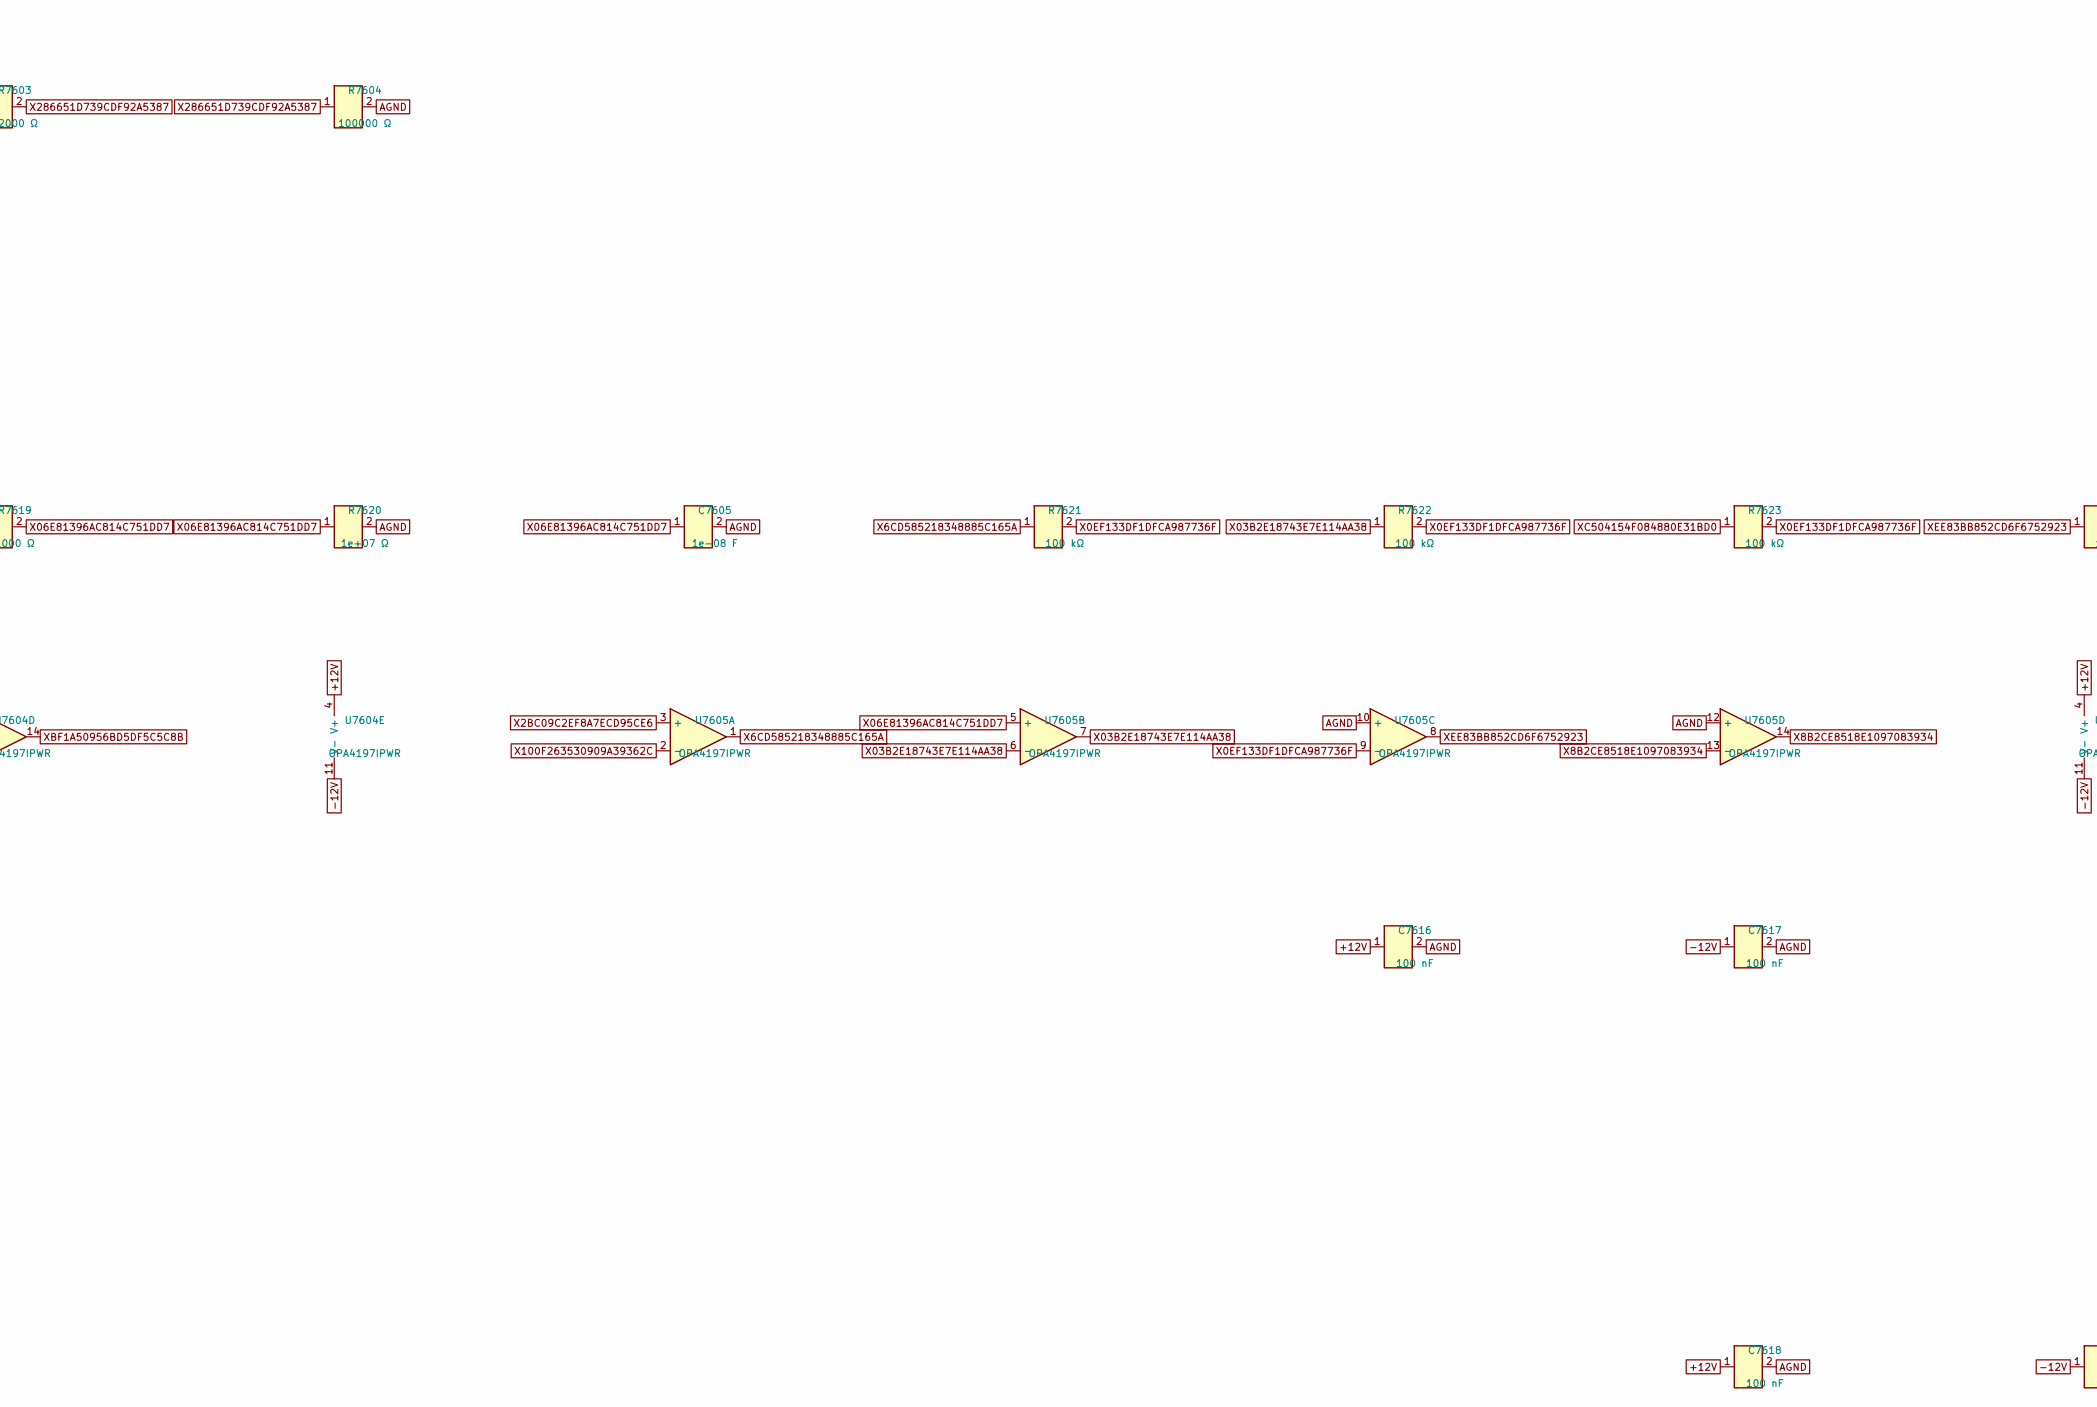
[picture p177: schematic offset_A06_K.kicad_sch, part in row 1, column 2]

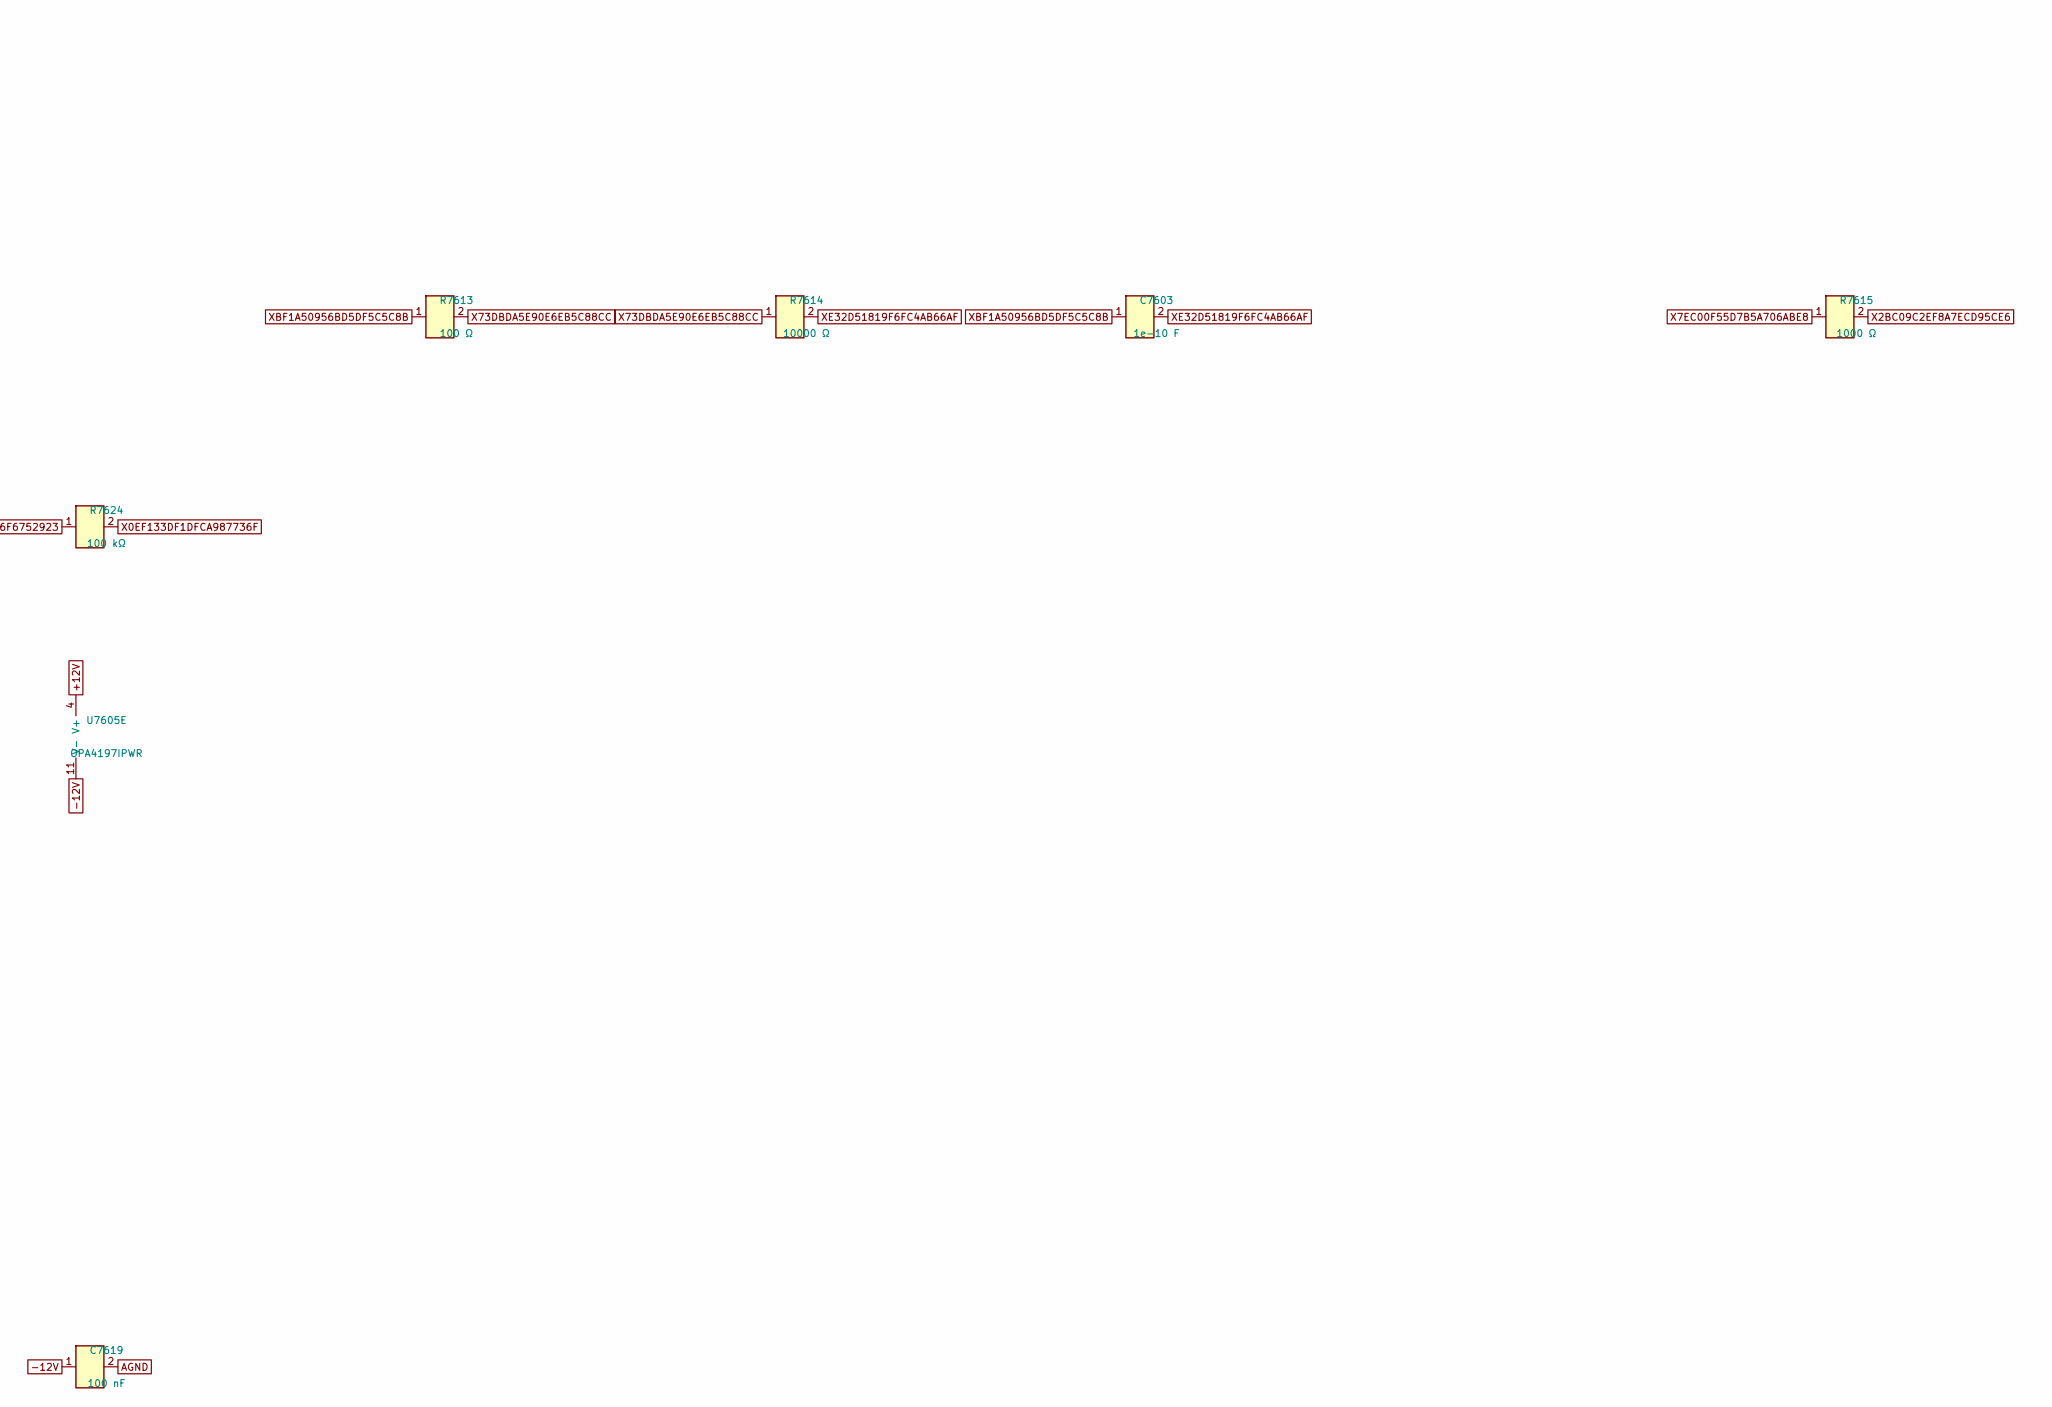
[picture p178: schematic offset_A06_K.kicad_sch, part in row 1, column 3]

Parts:
C7601: 1e-07 F; C0603; MPN GRM188R71H104KA93D
C7602: 1e-06 F; C0603
C7603: 1e-10 F; C0603; MPN C0603C101J5GACTU
C7604: 1e-11 F; C0603
C7605: 1e-08 F; C0603
C7607, C7616, C7617, C7618, C7619: 100 nF; C0603; MPN GRM188R71H104KA93D
R7601, R7602, R7614: 10000 Ω; R0603
R7603: 22000 Ω; R0603
R7604, R7617, R7618: 100000 Ω; R0603; MPN RT0603BRD07100KL
R7613: 100 Ω; R0603
R7615, R7619: 1000 Ω; R0603
R7616, R7620: 1e+07 Ω; R0603
R7621, R7622, R7623, R7624: 100 kΩ; R0603; MPN RT0603BRD07100KL
U7601: REF5050AIDR; SOIC-8_3.9x4.9mm_P1.27mm; MPN REF5050AIDR; LCSC C27804
U7604, U7605: OPA4197IPWR; TSSOP-14_4.4x5mm_P0.65mm; MPN OPA4197IPWR; LCSC C2057327

Connections:
+12V: C7601.1, C7607.1, C7616.1, C7618.1, U7601.2 (Vin), U7604.4 (V+), U7605.4 (V+)
-12V: C7617.1, C7619.1, U7604.11 (V-), U7605.11 (V-)
AGND: C7601.2, C7602.2, C7605.2, C7607.2, C7616.2, C7617.2, C7618.2, C7619.2, R7604.2, R7616.2, R7620.2, U7601.4 (GND), U7604.5 (+), U7605.10 (+), U7605.12 (+)
X0D2E42FC8CDE3604A8C3: U7604.8, U7604.9 (-)
X0EF133DF1DFCA987736F: R7621.2, R7622.2, R7623.2, R7624.2, U7605.9 (-)
X2BC09C2EF8A7ECD95CE6: R7615.2, R7616.1, U7605.3 (+)
X2D597327EED2D1A7509E: R7602.1, U7604.7
X2DD640CDE246E1F97E07: R7601.2, R7602.2, U7604.6 (-)
X03B2E18743E7E114AA38: R7622.1, U7605.6 (-), U7605.7
X6CD585218348885C165A: C7604.1, R7618.1, R7621.1, U7605.1
X06E81396AC814C751DD7: C7605.1, R7619.2, R7620.1, U7605.5 (+)
X7EC00F55D7B5A706ABE8: R7615.1
X8B2CE8518E1097083934: U7605.13 (-), U7605.14
X45AEDA7EA8DE3AE9B3ED: R7601.1, R7603.1, U7604.1, U7604.2 (-)
X73DBDA5E90E6EB5C88CC: R7613.2, R7614.1
X100F263530909A39362C: C7604.2, R7617.2, R7618.2, U7605.2 (-)
X265FED80190F5E11B071: R7617.1, U7604.12 (+)
X286651D739CDF92A5387: R7603.2, R7604.1, U7604.10 (+)
XBF1A50956BD5DF5C5C8B: C7603.1, R7613.1, U7604.14
XC504154F084880E31BD0: R7623.1
XE32D51819F6FC4AB66AF: C7603.2, R7614.2, U7604.13 (-)
XECF2E811656C746385DF: R7619.1
XEE83BB852CD6F6752923: R7624.1, U7605.8
XF64B2591D1632A63D37C: C7602.1, U7601.6 (Vout), U7604.3 (+)
