Takazudo/zudo-osc-hole-field/boards/osc-core/sheets/oscillator_O1_K.kicad_sch

## KiCad design boards/osc-core/sheets/oscillator_O1_K.kicad_sch (2026-10-05)

Schematic: oscillator_O1_K.kicad_sch

Parts:
C1101, C1103: 1e-10 F; C0603; MPN C0603C101J5GACTU
C1102, C1104: 1e-11 F; C0603
C1105, C1106, C1107: 1e-08 F; C0603
C1108, C1110, C1129, C1130, C1131, C1132, C1133, C1134, C1135, C1136, C1137, C1138, C1139, C1142, C1143, C1144, C1145, C1146, C1147, C1148, C1149: 100 nF; C0603; MPN GRM188R71H104KA93D
C1109: 100 pF; C0603; MPN C0603C101J5GACTU
C1111: 1 nF C0G; C0603
C1112: 10 nF; C0603
C1113, C1114, C1115, C1116, C1117, C1118, C1119, C1120: 1 nF; C0603
DO1105: BAT54S,215; SOT-23; MPN BAT54S,215
Q1101: BCM847BS,115; SOT-363_SC-70-6; MPN BCM847BS,115
R1117, R1123, R1148: 100 Ω; R0603
R1118, R1124, R1158: 10000 Ω; R0603
R1119, R1125, R1129, R1131, R1133: 1000 Ω; R0603
R1120, R1126, R1130, R1132, R1134: 1e+07 Ω; R0603
R1121, R1122, R1127, R1128, R1156: 100000 Ω; R0603; MPN RT0603BRD07100KL
R1135, R1190: 1 kΩ; R0603
R1136, R1139: 10 MΩ; R0603
R1137, R1176: 40 kΩ; R0603
R1138, R1140, R1141, R1145, R1161, R1163, R1166, R1169, R1170, R1172, R1175, R1177, R1179, R1181, R1182, R1183, R1184, R1185, R1187, R1188, R1195, R1196, R1197, R1198, R1199: 100 kΩ; R0603; MPN RT0603BRD07100KL
R1142, R1174: 250 kΩ; R0603
R1143: 5 MΩ; R0603
R1144, R1167: 200 kΩ; R0603
R1146: 82.5 kΩ; R0603
R1147, R1191: 1 MΩ; R0603
R1149, R1162, R1164, R1173, R1192, R1193, R1194: 10 kΩ; R0603
R1150: 24 kΩ; R0603
R1151: 5.72 kΩ; R0603
R1152: 1.5 kΩ; R0603
R1153: 1.2 MΩ; R0603
R1154: 470 Ω; R0603
R1155: 51 kΩ; R0603
R1157: 33200 Ω; R0603
R1159: 390000 Ω; R0603
R1160: 4700 Ω; R0603
R1165: 72 kΩ; R0603
R1168: 1.8 MΩ; R0603
R1171: 25 kΩ; R0603
R1178: 125 kΩ; R0603
R1180: 80 kΩ; R0603
R1186: 4.7 kΩ; R0603
R1189: 68 kΩ; R0603
RB1101: 49.9 kΩ; R0603
RB1110, RB1111, RB1112, RB1113, RB1114, RB1115, RB1116, RB1117, RB1118, RB1119, RB1120, RB1121: 100 Ω; R0603
RVO1106, RVO1107, RVO1110, RVO1111: 10 kΩ; Potentiometer_Bourns_TC33X_Vertical; MPN TC33X-2-103E
RVO1108: 1 kΩ; Potentiometer_Bourns_TC33X_Vertical; MPN TC33X-2-102E
RVO1109: 20 kΩ; Potentiometer_Bourns_TC33X_Vertical
U1105: AS3340D; SOIC-16_3.9x9.9mm_P1.27mm; MPN AS3340D
U1106, U1108: LM393BIDR; SOIC-8_3.9x4.9mm_P1.27mm; MPN LM393BIDR
U1107: SN74HC14DR; SOIC-14_3.9x8.7mm_P1.27mm; MPN SN74HC14DR
U1109, U1110, U1111: OPA4197IPWR; TSSOP-14_4.4x5mm_P0.65mm; MPN OPA4197IPWR; LCSC C2057327
U1112, U1113, U1114, U1115: OPA4196IDR; SOIC-14_3.9x8.7mm_P1.27mm; MPN OPA4196IDR; LCSC C2057385

Connections:
+5V: C1132.1, R1160.1, R1186.1, U1106.6 (-), U1107.14 (VCC), U1108.6 (-)
+12V: C1129.1, C1131.1, C1133.1, C1134.1, C1136.1, C1138.1, C1142.1, C1144.1, C1146.1, C1148.1, R1153.1, R1193.1, R1194.1, U1105.16 (VCC), U1106.8 (V+), U1108.8 (V+), U1109.4 (V+), U1110.4 (V+), U1111.4 (V+), U1112.4 (V+), U1113.4 (V+), U1114.4 (V+), U1115.4 (V+)
-12V: C1135.1, C1137.1, C1139.1, C1143.1, C1145.1, C1147.1, C1149.1, R1192.2, U1109.11 (V-), U1110.11 (V-), U1111.11 (V-), U1112.11 (V-), U1113.11 (V-), U1114.11 (V-), U1115.11 (V-)
AGND: C1105.2, C1106.2, C1107.2, C1108.2, C1110.2, C1111.2, C1112.2, C1129.2, C1130.2, C1131.2, C1132.2, C1133.2, C1134.2, C1135.2, C1136.2, C1137.2, C1138.2, C1139.2, C1142.2, C1143.2, C1144.2, C1145.2, C1146.2, C1147.2, C1148.2, C1149.2, DO1105.1 (A), Q1101.5 (B2), R1120.2, R1126.2, R1130.2, R1132.2, R1134.2, R1136.2, R1138.2, R1139.2, R1151.2, R1155.2, R1161.2, R1163.2, R1172.2, R1175.2, R1179.2, R1183.2, R1185.2, R1190.2, R1196.2, RVO1107.2 (Wiper), RVO1107.3 (CW), RVO1108.2 (Wiper), RVO1108.3 (CW), RVO1109.3 (CW), U1105.12 (GND), U1106.4 (GND), U1106.5 (+), U1107.3, U1107.5, U1107.7 (GND), U1107.9, U1107.11, U1107.13, U1108.4 (GND), U1108.5 (+), U1111.10 (+), U1111.12 (+), U1113.10 (+), U1113.12 (+), U1115.5 (+), U1115.10 (+), U1115.12 (+)
X0A34A50EAB62B0C19178: R1176.2, R1177.2, U1114.6 (-)
X0C487389EDA1C803A833: R1139.1, R1145.1
X0E24CD1EAF3087664A23: C1119.1, RB1118.1, U1111.1
X0ED6F78F7B67ABB40FB7: R1182.2, R1183.1, U1108.2 (-)
X0EF916B0CB53D9F46426: R1156.1
X1C3D5718BB374D438516: C1112.1, R1154.2
X1D6A57CAF669481E86FF: C1102.1, R1122.1, R1144.1, U1112.7
X1E5B73B2807B83DA3BA9: C1113.2, U1105.9 (VSSI)
X1F43213A02655CCA2673: RB1116.2, RB1117.1, RVO1106.1 (CCW)
X1FDAF036C32846AE10D6: R1141.1, U1109.8, U1109.9 (-)
X2EDDFA4BD6FE39CB6327: R1152.2, RVO1108.1 (CCW)
X3AC1E8E01E953B9F2A6A: DO1105.2 (K), U1114.1, U1114.2 (-)
X3AF346782A256D664849: R1156.2, R1157.2, U1106.2 (-)
X3C23D7180C78ECD75117: Q1101.3 (C2), R1194.2, R1195.1
X3F10D13DDDFC81882CF3: C1114.1, R1164.2
X4F4C65A27511338D257C: RVO1109.1 (CCW), U1105.7 (VHFT)
X4F82C77EF7F47F31A68A: U1107.2
X4FBEF1511A375A9CD95E: R1159.1, R1160.2, U1106.1, U1107.1
X6A4B8EF46A80D98620E0: U1110.3 (+), U1110.10 (+), U1111.3 (+)
X6A3489D2F2EFF8F97940: C1120.2, RB1121.2, U1111.6 (-)
X6AB9F03B874531733044: R1165.2, R1166.2, R1167.2, R1168.2, U1113.9 (-)
X06F4FAD20156FA9A9042: R1169.2, R1170.2, U1113.13 (-)
X07C8B66CE17B1F170A9D: C1101.1, R1117.1, U1112.1
X7F38E95E8772C9958C4A: R1171.2, R1172.1, U1114.3 (+)
X8A34FB719E211DCF932D: R1199.2, RVO1111.2 (Wiper), RVO1111.3 (CW), U1115.6 (-)
X8CEAB634DFB5229AF7B5: R1176.1, U1105.10 (VTO)
X8D47F4038AE6E42915B2: R1137.1, U1113.7
X9C748609E0A53AF1C2E3: R1151.1, U1105.2 (SCALE2)
X9CFBC291C1BD017FC0A9: R1137.2, R1138.1, U1113.6 (-)
X9E472E51C7738C111D95: C1101.2, R1118.2, U1112.2 (-)
X9F9601A9B70D8A94B724: R1140.2, R1141.2, R1142.2, R1143.2, R1144.2, R1145.2, R1146.2, R1147.2, U1105.15 (VFCI)
X9F47443B516E90FF872D: RB1112.2, RB1113.1, U1109.12 (+), U1113.5 (+)
X18B799A5334D35AC7DA4: C1111.1, U1105.11 (CAP)
X35F06C13DA9B0DF7D226: C1102.2, R1121.2, R1122.2, U1112.6 (-)
X43F52BB22568DC01B6EA: RB1101.2, RVO1111.1 (CCW)
X44CC9CDFCD3CBADF5D00: R1131.1
X47C2211BADF82245E208: R1187.1, U1114.14
X47CDB73EF89C07E59C0F: R1140.1
X49D4A828C61E52E9711A: R1198.1, R1199.1, U1115.1
X50C8E3ED76C5951C6BA3: C1115.2, RB1111.2, U1110.2 (-)
X53DC1931CA4333ABAB04: C1103.2, R1124.2, U1112.9 (-)
X78F73E5AB30C238838B9: R1178.2, R1179.1, U1114.10 (+)
X88BCE8602AF7844F3340: R1155.1, R1182.1, U1105.4 (VP)
X89A1C053ECCC5FC2B3AC: C1104.2, R1127.2, R1128.2, U1112.13 (-)
X89EADF9E5E333492838A: R1119.2, R1120.1, U1112.5 (+)
X89FA9515372969F8D13C: R1158.1
X90EEDB72A75DC6F13F0D: R1135.1
X96BBBE7E2F6614FCFBA7: C1130.1, R1148.2, R1149.1, U1105.3 (VEE)
X110EF417EBA43801D3CA: R1117.2, R1118.1
X526EDAE6B1ABDD39FB33: R1195.2, R1196.1, U1115.3 (+)
X564E0D4370AA70AB7B55: R1186.2, U1108.1, U1114.12 (+)
X722B62B5E67741B855CA: RB1101.1, U1115.7
X763E77DF6D4025E687FA: R1163.1, R1164.1
X854D05A10C45490AF4AA: C1108.1, R1135.2, R1136.1, U1109.10 (+)
X949BAE27CBD25DDA5726: C1110.1, R1152.1, U1105.14 (VS)
X1822B8D41EBA95CBC363: Q1101.2 (B1), R1189.2, R1190.1, R1191.2
X2842A95258EB703DE67C: R1146.1, R1157.1, R1168.1, R1171.1, R1174.1, R1178.1, R1184.1, R1188.1, RB1110.2, RB1111.1
X3717B79E5D5CB90202D0: Q1101.1 (E1), Q1101.4 (E2), R1192.1
X03899EF77CFB15DF4250: R1161.1, R1162.1
X7396CCB03EC92D63D81A: U1115.13 (-), U1115.14
X7858CBBD1598D7E90ED6: C1107.1, R1133.2, R1134.1, U1113.3 (+)
X9839BD653817195FB9B1: C1106.1, R1131.2, R1132.1, U1109.5 (+)
X12379E548CE520E434AF: C1119.2, RB1119.2, U1111.2 (-)
X91321E5C2E8A8E4376F3: C1116.2, RB1113.2, U1110.6 (-)
X200571CDE8D39E212FD5: R1170.1, R1173.1, U1113.14
X275914F8D0058F71EFF0: R1123.2, R1124.1
X283762E52614D8D51C1A: R1181.1, U1114.8
X699048DF1C17BB355894: R1125.1
X0999457B7EE4B0B47AC6: R1191.1, RVO1110.2 (Wiper)
X4600622B0B64BE00D88E: C1115.1, RB1110.1, U1110.1
X9602156FBE841AD44944: R1180.2, R1181.2, U1114.9 (-)
X99031427EC4E7C0E3862: C1109.2, R1149.2, U1109.13 (-)
X394087072DAEF9F4226C: U1110.5 (+), U1110.12 (+), U1111.5 (+)
XA5F650FE3E97CBF41AB3: R1129.1
XA921D046306EA279E461: C1105.1, R1129.2, R1130.1, U1109.3 (+)
XADB906B43917B481E867: R1133.1
XAEA61CD2900940C9BFFC: R1180.1, U1105.8 (VSO)
XB2DF0C8BD783E9925228: R1174.2, R1175.1, U1114.5 (+)
XB53AD31902607C80D653: R1143.1, U1109.6 (-), U1109.7
XB71FDC5E00519B11EB3D: C1117.1, RB1114.1, U1110.8
XB5379E455BFA1F7768BC: R1142.1, U1109.1, U1109.2 (-)
XBA1BD421D271CD94C645: C1116.1, RB1112.1, U1110.7
XBA3E9C437B4E486D623D: R1127.1, U1112.10 (+)
XBD85EECA989B96798CD8: RB1120.2, RB1121.1, RVO1110.1 (CCW)
XBE4B8F421A817D1D5966: C1114.2, U1105.6 (VHSI)
XBF9B72AAC6231943B92D: C1103.1, R1123.1, U1112.8
XBF999C23E3F2C661A4DA: R1125.2, R1126.1, U1112.12 (+)
XC1DDD03E75BA1472A1E3: C1117.2, RB1115.2, U1110.9 (-)
XC6D63AA9EAFF9BA1AE05: RB1114.2, RB1115.1, RVO1106.3 (CW)
XC7D2E17C292CA8FB7EE6: R1150.1, U1105.1 (SCALE1)
XC4187D9B3C74E77AB2D2: C1104.1, R1128.1, R1167.1, U1112.14
XC32246735229F8678699: R1158.2, R1159.2, U1106.3 (+)
XCDB392101F7276A507EC: R1177.1, R1189.1, U1114.7
XD3B6006A77722B5ADA8E: R1197.2, R1198.2, U1115.2 (-)
XD6A1F9F8DC2B19A4D354: R1153.2, R1154.1, RVO1109.2 (Wiper), U1105.13 (VLFI)
XD9E5E080F173E1F55A12: C1118.2, RB1117.2, U1110.13 (-)
XD7417BCEB79D0EB5DC72: Q1101.6 (C1), R1193.2, R1197.1
XDDEDFF17E81C645ACF69: R1184.2, R1185.1, U1108.3 (+)
XE23CA6065976CA4970D0: R1147.1, RVO1106.2 (Wiper)
XE888FA3A0567B6436555: R1165.1, R1169.1, U1113.8
XE62612A635A279202EF1: C1113.1, R1162.2
XEBAB596A81C6BFCCB1F8: R1166.1, U1113.1, U1113.2 (-)
XEBFA5F251E72BD4CF173: R1187.2, R1188.2, U1114.13 (-)
XEC99E592A6831E7B221E: C1120.1, RB1120.1, U1111.7
XED305DE8B32BE6A78938: C1118.1, RB1116.1, U1110.14
XEF7AB25C895EBFD6768C: C1109.1, R1148.1, U1109.14
XF2E7C6D95746DE0DC121: U1115.8, U1115.9 (-)
XF7E00CDC39C343B166E7: RB1118.2, RB1119.1, RVO1110.3 (CW)
XF7EA89F146B5CCC921B7: R1150.2, RVO1107.1 (CCW)
XF54DFAD185ACEE0F7BC4: DO1105.3 (COM), R1173.2, U1105.5 (VPWM)
XF72FCCEB469282F935FB: U1111.8, U1111.9 (-)
XF772FCDBDE0140AA96B6: U1111.13 (-), U1111.14
XFCBF7CEE1BED9441283A: R1121.1, U1112.3 (+)
XFF51449A8957A022385F: R1119.1
