Takazudo/zudo-osc-hole-field/boards/osc-core/sheets/oscillator_O2_K.kicad_sch

## KiCad design boards/osc-core/sheets/oscillator_O2_K.kicad_sch (2026-10-05)

Schematic: oscillator_O2_K.kicad_sch

Parts:
C1201, C1203: 1e-10 F; C0603; MPN C0603C101J5GACTU
C1202, C1204: 1e-11 F; C0603
C1205, C1206, C1207: 1e-08 F; C0603
C1208, C1210, C1229, C1230, C1231, C1232, C1233, C1234, C1235, C1236, C1237, C1238, C1239, C1242, C1243, C1244, C1245, C1246, C1247, C1248, C1249: 100 nF; C0603; MPN GRM188R71H104KA93D
C1209: 100 pF; C0603; MPN C0603C101J5GACTU
C1211: 1 nF C0G; C0603
C1212: 10 nF; C0603
C1213, C1214, C1215, C1216, C1217, C1218, C1219, C1220: 1 nF; C0603
DO1205: BAT54S,215; SOT-23; MPN BAT54S,215
Q1201: BCM847BS,115; SOT-363_SC-70-6; MPN BCM847BS,115
R1217, R1223, R1248: 100 Ω; R0603
R1218, R1224, R1258: 10000 Ω; R0603
R1219, R1225, R1229, R1231, R1233: 1000 Ω; R0603
R1220, R1226, R1230, R1232, R1234: 1e+07 Ω; R0603
R1221, R1222, R1227, R1228, R1256: 100000 Ω; R0603; MPN RT0603BRD07100KL
R1235, R1290: 1 kΩ; R0603
R1236, R1239: 10 MΩ; R0603
R1237, R1276: 40 kΩ; R0603
R1238, R1240, R1241, R1245, R1261, R1263, R1266, R1269, R1270, R1272, R1275, R1277, R1279, R1281, R1282, R1283, R1284, R1285, R1287, R1288, R1295, R1296, R1297, R1298, R1299: 100 kΩ; R0603; MPN RT0603BRD07100KL
R1242, R1274: 250 kΩ; R0603
R1243: 5 MΩ; R0603
R1244, R1267: 200 kΩ; R0603
R1246: 82.5 kΩ; R0603
R1247, R1291: 1 MΩ; R0603
R1249, R1262, R1264, R1273, R1292, R1293, R1294: 10 kΩ; R0603
R1250: 24 kΩ; R0603
R1251: 5.72 kΩ; R0603
R1252: 1.5 kΩ; R0603
R1253: 1.2 MΩ; R0603
R1254: 470 Ω; R0603
R1255: 51 kΩ; R0603
R1257: 33200 Ω; R0603
R1259: 390000 Ω; R0603
R1260: 4700 Ω; R0603
R1265: 72 kΩ; R0603
R1268: 1.8 MΩ; R0603
R1271: 25 kΩ; R0603
R1278: 125 kΩ; R0603
R1280: 80 kΩ; R0603
R1286: 4.7 kΩ; R0603
R1289: 68 kΩ; R0603
RB1201: 49.9 kΩ; R0603
RB1210, RB1211, RB1212, RB1213, RB1214, RB1215, RB1216, RB1217, RB1218, RB1219, RB1220, RB1221: 100 Ω; R0603
RVO1206, RVO1207, RVO1210, RVO1211: 10 kΩ; Potentiometer_Bourns_TC33X_Vertical; MPN TC33X-2-103E
RVO1208: 1 kΩ; Potentiometer_Bourns_TC33X_Vertical; MPN TC33X-2-102E
RVO1209: 20 kΩ; Potentiometer_Bourns_TC33X_Vertical
U1205: AS3340D; SOIC-16_3.9x9.9mm_P1.27mm; MPN AS3340D
U1206, U1208: LM393BIDR; SOIC-8_3.9x4.9mm_P1.27mm; MPN LM393BIDR
U1207: SN74HC14DR; SOIC-14_3.9x8.7mm_P1.27mm; MPN SN74HC14DR
U1209, U1210, U1211: OPA4197IPWR; TSSOP-14_4.4x5mm_P0.65mm; MPN OPA4197IPWR; LCSC C2057327
U1212, U1213, U1214, U1215: OPA4196IDR; SOIC-14_3.9x8.7mm_P1.27mm; MPN OPA4196IDR; LCSC C2057385

Connections:
+5V: C1232.1, R1260.1, R1286.1, U1206.6 (-), U1207.14 (VCC), U1208.6 (-)
+12V: C1229.1, C1231.1, C1233.1, C1234.1, C1236.1, C1238.1, C1242.1, C1244.1, C1246.1, C1248.1, R1253.1, R1293.1, R1294.1, U1205.16 (VCC), U1206.8 (V+), U1208.8 (V+), U1209.4 (V+), U1210.4 (V+), U1211.4 (V+), U1212.4 (V+), U1213.4 (V+), U1214.4 (V+), U1215.4 (V+)
-12V: C1235.1, C1237.1, C1239.1, C1243.1, C1245.1, C1247.1, C1249.1, R1292.2, U1209.11 (V-), U1210.11 (V-), U1211.11 (V-), U1212.11 (V-), U1213.11 (V-), U1214.11 (V-), U1215.11 (V-)
AGND: C1205.2, C1206.2, C1207.2, C1208.2, C1210.2, C1211.2, C1212.2, C1229.2, C1230.2, C1231.2, C1232.2, C1233.2, C1234.2, C1235.2, C1236.2, C1237.2, C1238.2, C1239.2, C1242.2, C1243.2, C1244.2, C1245.2, C1246.2, C1247.2, C1248.2, C1249.2, DO1205.1 (A), Q1201.5 (B2), R1220.2, R1226.2, R1230.2, R1232.2, R1234.2, R1236.2, R1238.2, R1239.2, R1251.2, R1255.2, R1261.2, R1263.2, R1272.2, R1275.2, R1279.2, R1283.2, R1285.2, R1290.2, R1296.2, RVO1207.2 (Wiper), RVO1207.3 (CW), RVO1208.2 (Wiper), RVO1208.3 (CW), RVO1209.3 (CW), U1205.12 (GND), U1206.4 (GND), U1206.5 (+), U1207.3, U1207.5, U1207.7 (GND), U1207.9, U1207.11, U1207.13, U1208.4 (GND), U1208.5 (+), U1211.10 (+), U1211.12 (+), U1213.10 (+), U1213.12 (+), U1215.5 (+), U1215.10 (+), U1215.12 (+)
X0B78D69DA859B032ED3C: R1286.2, U1208.1, U1214.12 (+)
X00D3BCB5E0AFD29A84DF: R1263.1, R1264.1
X0FB264EF44DB42001836: Q1201.1 (E1), Q1201.4 (E2), R1292.1
X1B26CE7C17DC28E88025: RB1216.2, RB1217.1, RVO1206.1 (CCW)
X1B89C9307954FD8B0BD8: R1295.2, R1296.1, U1215.3 (+)
X1D4C6918F975CB51B337: C1214.2, U1205.6 (VHSI)
X1FC395EA34B7BC392223: Q1201.3 (C2), R1294.2, R1295.1
X2FE4AF262FF60AFC8887: R1227.1, U1212.10 (+)
X4D2E0C8D405D9E91F1EF: C1206.1, R1231.2, R1232.1, U1209.5 (+)
X4E741E95F97DF52231DC: R1265.2, R1266.2, R1267.2, R1268.2, U1213.9 (-)
X04EB6B3DC069E08BFECF: R1233.1
X4F06610A1F9AD3EA241D: R1265.1, R1269.1, U1213.8
X5B4E142B0D33DFB0F44C: C1207.1, R1233.2, R1234.1, U1213.3 (+)
X5C393E992DE8FBABF769: C1201.1, R1217.1, U1212.1
X5F2D6FC1B7B9A50CA526: R1259.1, R1260.2, U1206.1, U1207.1
X6A4B8EF46A80D98620E0: U1210.3 (+), U1210.10 (+), U1211.3 (+)
X6C085B63BE4EF675AF16: C1212.1, R1254.2
X6DCF966CBCDC52115B75: R1255.1, R1282.1, U1205.4 (VP)
X6E4708860137D063713F: R1253.2, R1254.1, RVO1209.2 (Wiper), U1205.13 (VLFI)
X6EC39B88F7DCE1663756: C1213.1, R1262.2
X6EC900BFC4E786DBBCF9: C1203.2, R1224.2, U1212.9 (-)
X7CA4825DF75BA1068B88: R1217.2, R1218.1
X7F050E716CD2F5112411: C1204.2, R1227.2, R1228.2, U1212.13 (-)
X8F5B42D1598BE65C0CCB: C1201.2, R1218.2, U1212.2 (-)
X8F240CED8F8E59366FA5: R1250.1, U1205.1 (SCALE1)
X9E8EB1B9DBAD2FA9BF2C: R1282.2, R1283.1, U1208.2 (-)
X20EB7398EF76F1D8670D: DO1205.2 (K), U1214.1, U1214.2 (-)
X22EF82418C7C113D22A9: R1277.1, R1289.1, U1214.7
X34F187E67693E5534719: C1218.2, RB1217.2, U1210.13 (-)
X37D3732191FF34D4A8EF: RB1214.2, RB1215.1, RVO1206.3 (CW)
X38F61A77B5274E1E98B7: C1215.2, RB1211.2, U1210.2 (-)
X41B88AA72B8A732B279A: RB1212.2, RB1213.1, U1209.12 (+), U1213.5 (+)
X41F90235F5D811F96597: C1219.2, RB1219.2, U1211.2 (-)
X43F9E199D2F6BE4D5C5B: R1297.2, R1298.2, U1215.2 (-)
X44C15FB5FCEE4833D007: C1205.1, R1229.2, R1230.1, U1209.3 (+)
X62CE6BDCCEE401D86E29: C1217.2, RB1215.2, U1210.9 (-)
X64D220928EDA3905C0D6: R1235.1
X66D4440212DCC1615507: R1270.1, R1273.1, U1213.14
X71A323211EF9F6803C80: R1237.2, R1238.1, U1213.6 (-)
X73FEA024826A273067D2: C1219.1, RB1218.1, U1211.1
X82D291B0D69033B085AF: C1217.1, RB1214.1, U1210.8
X89FA9515372969F8D13C: R1258.1
X90B993BFD6B3351086B1: Q1201.6 (C1), R1293.2, R1297.1
X92F7EC5BF13E7E12AB51: R1261.1, R1262.1
X245C8A88BDE6BBB78DF6: R1287.1, U1214.14
X283C96745F9A97C9F70D: RVO1209.1 (CCW), U1205.7 (VHFT)
X00444C74247F40210707: RB1201.1, U1215.7
X476A5E5F74F17D909525: R1278.2, R1279.1, U1214.10 (+)
X494A69F57398E0094B88: R1239.1, R1245.1
X602FEC569CB78ADD80C9: R1276.1, U1205.10 (VTO)
X615B5451A30EFB7514FF: U1211.13 (-), U1211.14
X653F33BFDEC7285E3F5F: C1209.2, R1249.2, U1209.13 (-)
X660EAF14A1830C30125B: R1241.1, U1209.8, U1209.9 (-)
X741DF1C2056440887FCB: R1231.1
X931E79E5D5D06724201E: R1256.1
X937FEB0F1940A3E66D0F: C1211.1, U1205.11 (CAP)
X947D4B49DF13D9BCAFA3: R1281.1, U1214.8
X1080B5575AB1BB1A0248: R1237.1, U1213.7
X1960FB281C5E0D54E04C: C1230.1, R1248.2, R1249.1, U1205.3 (VEE)
X2520AFD5FAC0D8E5E4F2: R1219.2, R1220.1, U1212.5 (+)
X2891C8B5F105CAF8E53B: R1291.1, RVO1210.2 (Wiper)
X2965CE20D2FE0AC8DDE2: R1240.2, R1241.2, R1242.2, R1243.2, R1244.2, R1245.2, R1246.2, R1247.2, U1205.15 (VFCI)
X6594A313DB0BD7CE2642: R1247.1, RVO1206.2 (Wiper)
X8389F51118AF24248D55: C1215.1, RB1210.1, U1210.1
X008537AA7400D5A1B933: R1240.1
X8883FE0F6182536E5030: R1252.2, RVO1208.1 (CCW)
X15938C42644C2F3EFBEE: R1229.1
X85403F578009F040AAE6: Q1201.2 (B1), R1289.2, R1290.1, R1291.2
X88892B40B9387F085BE0: R1284.2, R1285.1, U1208.3 (+)
X128438BC8E38CBB3D6A9: R1242.1, U1209.1, U1209.2 (-)
X369469A76F21E0FFAAB2: C1203.1, R1223.1, U1212.8
X705477C80EDE28FDEBED: DO1205.3 (COM), R1273.2, U1205.5 (VPWM)
X0852373C2151B421A87D: R1266.1, U1213.1, U1213.2 (-)
X4070539D709C19A0AF65: R1221.1, U1212.3 (+)
X07091428A2F296D4CAB7: C1220.1, RB1220.1, U1211.7
X9207009C66911DAAEE94: R1299.2, RVO1211.2 (Wiper), RVO1211.3 (CW), U1215.6 (-)
X52268074E547F37C1BDF: U1207.2
X394087072DAEF9F4226C: U1210.5 (+), U1210.12 (+), U1211.5 (+)
X83676898819EC6E16970: R1274.2, R1275.1, U1214.5 (+)
XA3E073702B5DFBF7E6A7: C1210.1, R1252.1, U1205.14 (VS)
XA5CDD378FBD65FC6D851: C1204.1, R1228.1, R1267.1, U1212.14
XACDF64E15274B67ECC5C: C1218.1, RB1216.1, U1210.14
XB090D2B1283E85C30458: C1209.1, R1248.1, U1209.14
XB101CAFF6544BE33EB4E: R1251.1, U1205.2 (SCALE2)
XB172D67E93F368A1180E: RB1218.2, RB1219.1, RVO1210.3 (CW)
XB3889EBCA57ED5116B49: C1220.2, RB1221.2, U1211.6 (-)
XBAFAADEA6FE714FBE0D5: RB1220.2, RB1221.1, RVO1210.1 (CCW)
XBB7C344851AF8D0601AC: R1246.1, R1257.1, R1268.1, R1271.1, R1274.1, R1278.1, R1284.1, R1288.1, RB1210.2, RB1211.1
XBBCB68EC84CFE7327976: C1213.2, U1205.9 (VSSI)
XBDE3139732CB12C98121: R1258.2, R1259.2, U1206.3 (+)
XBF5F9E9E3A35090372FC: R1269.2, R1270.2, U1213.13 (-)
XC939B35A76A5DCA1183F: R1287.2, R1288.2, U1214.13 (-)
XC232972A97598E6A166D: R1280.2, R1281.2, U1214.9 (-)
XC07537980965E3F148B6: R1271.2, R1272.1, U1214.3 (+)
XCB9A67475A24D2E7FEE9: RB1201.2, RVO1211.1 (CCW)
XCC0109184A2488FD3CDF: U1215.13 (-), U1215.14
XCC1350026597CEE286BE: R1219.1
XCF6DED013D11897BC17C: C1202.1, R1222.1, R1244.1, U1212.7
XCF09988C6EB590BA658A: U1211.8, U1211.9 (-)
XD2F1D07A3510A1E00D4F: R1256.2, R1257.2, U1206.2 (-)
XD90BCA73D92A618F8370: R1250.2, RVO1207.1 (CCW)
XD4682362CD25092A347B: R1225.1
XDC4E3FC2B318B08649AA: C1214.1, R1264.2
XDF69E8E6109A8944D128: R1225.2, R1226.1, U1212.12 (+)
XE199F24543D4BE605F31: R1280.1, U1205.8 (VSO)
XE354F809A31E03FF4584: C1216.1, RB1212.1, U1210.7
XEA4A9584DCFC3B93EB02: C1202.2, R1221.2, R1222.2, U1212.6 (-)
XEA613D24C48E0ECDD99A: C1208.1, R1235.2, R1236.1, U1209.10 (+)
XF1EBD465D8DD5809EB46: R1223.2, R1224.1
XF45DDE72C0A6584A089A: R1276.2, R1277.2, U1214.6 (-)
XF947C0129AA47F6B7F84: R1298.1, R1299.1, U1215.1
XFC0CF50B5DBD90EC2273: R1243.1, U1209.6 (-), U1209.7
XFC20E27CEEE292C63A99: U1215.8, U1215.9 (-)
XFE4AF1A52EF99B8410D0: C1216.2, RB1213.2, U1210.6 (-)
