Takazudo/zudo-osc-hole-field/boards/osc-core/sheets/oscillator_O3_K.kicad_sch

## KiCad design boards/osc-core/sheets/oscillator_O3_K.kicad_sch (2026-10-05)

Schematic: oscillator_O3_K.kicad_sch

Parts:
C1301, C1303: 1e-10 F; C0603; MPN C0603C101J5GACTU
C1302, C1304: 1e-11 F; C0603
C1305, C1306, C1307: 1e-08 F; C0603
C1308, C1310, C1329, C1330, C1331, C1332, C1333, C1334, C1335, C1336, C1337, C1338, C1339, C1342, C1343, C1344, C1345, C1346, C1347, C1348, C1349: 100 nF; C0603; MPN GRM188R71H104KA93D
C1309: 100 pF; C0603; MPN C0603C101J5GACTU
C1311: 1 nF C0G; C0603
C1312: 10 nF; C0603
C1313, C1314, C1315, C1316, C1317, C1318, C1319, C1320: 1 nF; C0603
DO1305: BAT54S,215; SOT-23; MPN BAT54S,215
Q1301: BCM847BS,115; SOT-363_SC-70-6; MPN BCM847BS,115
R1317, R1323, R1348: 100 Ω; R0603
R1318, R1324, R1358: 10000 Ω; R0603
R1319, R1325, R1329, R1331, R1333: 1000 Ω; R0603
R1320, R1326, R1330, R1332, R1334: 1e+07 Ω; R0603
R1321, R1322, R1327, R1328, R1356: 100000 Ω; R0603; MPN RT0603BRD07100KL
R1335, R1390: 1 kΩ; R0603
R1336, R1339: 10 MΩ; R0603
R1337, R1376: 40 kΩ; R0603
R1338, R1340, R1341, R1345, R1361, R1363, R1366, R1369, R1370, R1372, R1375, R1377, R1379, R1381, R1382, R1383, R1384, R1385, R1387, R1388, R1395, R1396, R1397, R1398, R1399: 100 kΩ; R0603; MPN RT0603BRD07100KL
R1342, R1374: 250 kΩ; R0603
R1343: 5 MΩ; R0603
R1344, R1367: 200 kΩ; R0603
R1346: 82.5 kΩ; R0603
R1347, R1391: 1 MΩ; R0603
R1349, R1362, R1364, R1373, R1392, R1393, R1394: 10 kΩ; R0603
R1350: 24 kΩ; R0603
R1351: 5.72 kΩ; R0603
R1352: 1.5 kΩ; R0603
R1353: 1.2 MΩ; R0603
R1354: 470 Ω; R0603
R1355: 51 kΩ; R0603
R1357: 33200 Ω; R0603
R1359: 390000 Ω; R0603
R1360: 4700 Ω; R0603
R1365: 72 kΩ; R0603
R1368: 1.8 MΩ; R0603
R1371: 25 kΩ; R0603
R1378: 125 kΩ; R0603
R1380: 80 kΩ; R0603
R1386: 4.7 kΩ; R0603
R1389: 68 kΩ; R0603
RB1301: 49.9 kΩ; R0603
RB1310, RB1311, RB1312, RB1313, RB1314, RB1315, RB1316, RB1317, RB1318, RB1319, RB1320, RB1321: 100 Ω; R0603
RVO1306, RVO1307, RVO1310, RVO1311: 10 kΩ; Potentiometer_Bourns_TC33X_Vertical; MPN TC33X-2-103E
RVO1308: 1 kΩ; Potentiometer_Bourns_TC33X_Vertical; MPN TC33X-2-102E
RVO1309: 20 kΩ; Potentiometer_Bourns_TC33X_Vertical
U1305: AS3340D; SOIC-16_3.9x9.9mm_P1.27mm; MPN AS3340D
U1306, U1308: LM393BIDR; SOIC-8_3.9x4.9mm_P1.27mm; MPN LM393BIDR
U1307: SN74HC14DR; SOIC-14_3.9x8.7mm_P1.27mm; MPN SN74HC14DR
U1309, U1310, U1311: OPA4197IPWR; TSSOP-14_4.4x5mm_P0.65mm; MPN OPA4197IPWR; LCSC C2057327
U1312, U1313, U1314, U1315: OPA4196IDR; SOIC-14_3.9x8.7mm_P1.27mm; MPN OPA4196IDR; LCSC C2057385

Connections:
+5V: C1332.1, R1360.1, R1386.1, U1306.6 (-), U1307.14 (VCC), U1308.6 (-)
+12V: C1329.1, C1331.1, C1333.1, C1334.1, C1336.1, C1338.1, C1342.1, C1344.1, C1346.1, C1348.1, R1353.1, R1393.1, R1394.1, U1305.16 (VCC), U1306.8 (V+), U1308.8 (V+), U1309.4 (V+), U1310.4 (V+), U1311.4 (V+), U1312.4 (V+), U1313.4 (V+), U1314.4 (V+), U1315.4 (V+)
-12V: C1335.1, C1337.1, C1339.1, C1343.1, C1345.1, C1347.1, C1349.1, R1392.2, U1309.11 (V-), U1310.11 (V-), U1311.11 (V-), U1312.11 (V-), U1313.11 (V-), U1314.11 (V-), U1315.11 (V-)
AGND: C1305.2, C1306.2, C1307.2, C1308.2, C1310.2, C1311.2, C1312.2, C1329.2, C1330.2, C1331.2, C1332.2, C1333.2, C1334.2, C1335.2, C1336.2, C1337.2, C1338.2, C1339.2, C1342.2, C1343.2, C1344.2, C1345.2, C1346.2, C1347.2, C1348.2, C1349.2, DO1305.1 (A), Q1301.5 (B2), R1320.2, R1326.2, R1330.2, R1332.2, R1334.2, R1336.2, R1338.2, R1339.2, R1351.2, R1355.2, R1361.2, R1363.2, R1372.2, R1375.2, R1379.2, R1383.2, R1385.2, R1390.2, R1396.2, RVO1307.2 (Wiper), RVO1307.3 (CW), RVO1308.2 (Wiper), RVO1308.3 (CW), RVO1309.3 (CW), U1305.12 (GND), U1306.4 (GND), U1306.5 (+), U1307.3, U1307.5, U1307.7 (GND), U1307.9, U1307.11, U1307.13, U1308.4 (GND), U1308.5 (+), U1311.10 (+), U1311.12 (+), U1313.10 (+), U1313.12 (+), U1315.5 (+), U1315.10 (+), U1315.12 (+)
X1A2F679EAD083BAAFCE8: R1356.2, R1357.2, U1306.2 (-)
X1B3E855D0EAF37C63927: R1317.2, R1318.1
X1B80C209713652D469B7: R1337.1, U1313.7
X1CAC315595BDC9472767: C1309.2, R1349.2, U1309.13 (-)
X1D5A2FDFB54CE963F21C: R1371.2, R1372.1, U1314.3 (+)
X1D77954A5FFD654FDE9A: Q1301.3 (C2), R1394.2, R1395.1
X01FF8FA844AA63688EED: RB1318.2, RB1319.1, RVO1310.3 (CW)
X2CA281339CB17909B79A: R1323.2, R1324.1
X2E6E3A5B3A1EDB8DE440: R1321.1, U1312.3 (+)
X2F7C12825727D31C59D7: Q1301.2 (B1), R1389.2, R1390.1, R1391.2
X3BE215420217265BBCC4: RB1312.2, RB1313.1, U1309.12 (+), U1313.5 (+)
X3CAE288E4112DC6F9BAF: R1370.1, R1373.1, U1313.14
X3EE60370B74B579C2DE9: RVO1309.1 (CCW), U1305.7 (VHFT)
X3F8B8ECAA0142C9FBAD9: C1305.1, R1329.2, R1330.1, U1309.3 (+)
X4ACF6BCBD80FF39F4684: R1356.1
X4AF7D7CB48E0DD51F79E: C1304.1, R1328.1, R1367.1, U1312.14
X4DD6838AF7D8A0F10F67: R1366.1, U1313.1, U1313.2 (-)
X5AC892F0D8CDA44E7E18: R1325.1
X5B762A6B5EA76653B214: R1376.1, U1305.10 (VTO)
X5C1753DA1FA241F3473E: C1317.2, RB1315.2, U1310.9 (-)
X5CD3D359D567354B0E0A: U1315.8, U1315.9 (-)
X5D31DD5D6E642F7542A9: R1335.1
X6A4B8EF46A80D98620E0: U1310.3 (+), U1310.10 (+), U1311.3 (+)
X6E3DEDE61BDE8E755183: C1316.1, RB1312.1, U1310.7
X7A359F260DFBAB14E990: C1308.1, R1335.2, R1336.1, U1309.10 (+)
X7A459576C684D0C8F155: R1343.1, U1309.6 (-), U1309.7
X7C941708F64519E8F815: R1399.2, RVO1311.2 (Wiper), RVO1311.3 (CW), U1315.6 (-)
X8D995226C23965D89DDD: R1369.2, R1370.2, U1313.13 (-)
X8E6C2D314FFC026A5210: R1374.2, R1375.1, U1314.5 (+)
X8F82F4DFE77F1C62D5E5: C1319.2, RB1319.2, U1311.2 (-)
X9C9F740D1C80B0BF2D2E: R1384.2, R1385.1, U1308.3 (+)
X9C285D3C07BA239ADB72: R1333.1
X9D2B06F1BC5228248BF8: R1387.1, U1314.14
X9D042D96389184586CCE: R1358.2, R1359.2, U1306.3 (+)
X24EFC14939D0DC268F8F: C1310.1, R1352.1, U1305.14 (VS)
X37C0D40E8793B92EA1B7: R1346.1, R1357.1, R1368.1, R1371.1, R1374.1, R1378.1, R1384.1, R1388.1, RB1310.2, RB1311.1
X39BA42DC7743B19B032C: C1316.2, RB1313.2, U1310.6 (-)
X41E885F0ECE415CBB61B: C1304.2, R1327.2, R1328.2, U1312.13 (-)
X53E6848A29A94622ABBC: R1339.1, R1345.1
X58FB9A53E02F27DA92B7: U1311.8, U1311.9 (-)
X59D0463557D2662EF25E: R1380.2, R1381.2, U1314.9 (-)
X073DB6E6783BC913BC5F: R1398.1, R1399.1, U1315.1
X080C9785421469AFF356: C1314.2, U1305.6 (VHSI)
X83EC03D998166A708B13: RB1320.2, RB1321.1, RVO1310.1 (CCW)
X89FA9515372969F8D13C: R1358.1
X94AAB7B98B263B18AD51: R1355.1, R1382.1, U1305.4 (VP)
X0541E095952FDD29D8F4: R1391.1, RVO1310.2 (Wiper)
X594BEAD28F1F55742288: R1376.2, R1377.2, U1314.6 (-)
X873FBDA9321D775F6874: RB1301.1, U1315.7
X901FA58E68E7F7016E8B: R1380.1, U1305.8 (VSO)
X966F4C38FA03A1A25AF4: R1327.1, U1312.10 (+)
X6641CDA99062907B3A69: R1319.1
X8275A6FC8406BA0717A9: U1311.13 (-), U1311.14
X17743E5166C7DE548F70: R1329.1
X36691C9E218105F4ACD0: R1337.2, R1338.1, U1313.6 (-)
X40950A1EE6676DBDA20C: R1325.2, R1326.1, U1312.12 (+)
X178317F81EE7702E7108: R1350.2, RVO1307.1 (CCW)
X229879FF828D5271ADF5: R1351.1, U1305.2 (SCALE2)
X905925DA2576F9B63E60: DO1305.2 (K), U1314.1, U1314.2 (-)
X3704315FCE39A9A8C581: RB1314.2, RB1315.1, RVO1306.3 (CW)
X5286894AC11ACE38D0D1: R1386.2, U1308.1, U1314.12 (+)
X5513000F5714CD71FAA8: C1320.1, RB1320.1, U1311.7
X394087072DAEF9F4226C: U1310.5 (+), U1310.12 (+), U1311.5 (+)
X618670950F5E3593AB56: C1313.2, U1305.9 (VSSI)
X9010280349C5FDB1AF4B: C1314.1, R1364.2
X634552790386BDD48BE1: DO1305.3 (COM), R1373.2, U1305.5 (VPWM)
XA03BF8E1475429AA7E90: R1359.1, R1360.2, U1306.1, U1307.1
XA7A6A80086D855A547BD: C1320.2, RB1321.2, U1311.6 (-)
XA019E807E2A752FFC687: R1363.1, R1364.1
XA873A418800EE67CBCE7: C1302.2, R1321.2, R1322.2, U1312.6 (-)
XA884168572A6DA25C2D9: C1315.1, RB1310.1, U1310.1
XAD74AFD348BF1546913D: U1315.13 (-), U1315.14
XB64EFBB63B79201CF71C: R1365.2, R1366.2, R1367.2, R1368.2, U1313.9 (-)
XB528E61191525CCF0307: U1307.2
XB858A65DCDBEE49EA1E4: Q1301.1 (E1), Q1301.4 (E2), R1392.1
XBA00A3C6EF612B611E92: R1353.2, R1354.1, RVO1309.2 (Wiper), U1305.13 (VLFI)
XBD26BB789358D3B9DF44: C1301.2, R1318.2, U1312.2 (-)
XBFCAE1684FF403A4AC4D: C1313.1, R1362.2
XC2D9A0E58D50465EDAF6: C1317.1, RB1314.1, U1310.8
XC49A5B1A6601C95C2803: R1350.1, U1305.1 (SCALE1)
XC186B79CB3F11FB9B048: C1318.1, RB1316.1, U1310.14
XC525ADDED3B005F989F0: C1315.2, RB1311.2, U1310.2 (-)
XC020594A376A964472E0: C1309.1, R1348.1, U1309.14
XC33487B6023F89EB5AC5: C1318.2, RB1317.2, U1310.13 (-)
XC36938B92385A9A06156: C1301.1, R1317.1, U1312.1
XCB7D4F22BD48FB8AFE01: R1365.1, R1369.1, U1313.8
XCB8F243280BA3BCBF8BE: C1311.1, U1305.11 (CAP)
XCBF504E8494703B7D2A8: C1306.1, R1331.2, R1332.1, U1309.5 (+)
XCFAFD68E163B49924004: C1319.1, RB1318.1, U1311.1
XD0DD7C8C9FD6FD1D00E1: R1347.1, RVO1306.2 (Wiper)
XD2A4EA3DC039EE4B9939: C1312.1, R1354.2
XD28ED4C8ADBB50D65408: R1381.1, U1314.8
XD48B80257A9D13E9B429: R1395.2, R1396.1, U1315.3 (+)
XD305DDFAE7E0616793A4: R1331.1
XD7793BDE625409267AB4: C1303.1, R1323.1, U1312.8
XD51322DA5CCAF0966272: R1361.1, R1362.1
XDDC5AE4A9EEF80CD646B: R1352.2, RVO1308.1 (CCW)
XDE7AB824E0E60E115AB7: R1377.1, R1389.1, U1314.7
XDE388D3AEC9B7B5D175D: R1341.1, U1309.8, U1309.9 (-)
XDED8FEDA7BF104736718: R1387.2, R1388.2, U1314.13 (-)
XDFB625F8D33B870AA8A2: R1340.1
XE40CE8B72EDAEF9AB614: Q1301.6 (C1), R1393.2, R1397.1
XE625950EDB15E05A8C21: C1307.1, R1333.2, R1334.1, U1313.3 (+)
XEB3ADF3D5A9AB1D27287: R1340.2, R1341.2, R1342.2, R1343.2, R1344.2, R1345.2, R1346.2, R1347.2, U1305.15 (VFCI)
XF2F37846271A8788AE2C: R1382.2, R1383.1, U1308.2 (-)
XF37E34E02DB6E5E9FDA5: RB1301.2, RVO1311.1 (CCW)
XF1979A951F195BAF1DB4: C1330.1, R1348.2, R1349.1, U1305.3 (VEE)
XF08710B2F7336807F592: R1397.2, R1398.2, U1315.2 (-)
XF70589A1841A9F6388AD: R1342.1, U1309.1, U1309.2 (-)
XF9044415FA54DBDAA101: R1378.2, R1379.1, U1314.10 (+)
XFE678195F71FDBB6B904: C1303.2, R1324.2, U1312.9 (-)
XFEA7225AA20958288FF0: C1302.1, R1322.1, R1344.1, U1312.7
XFF797ADD997B736FC7D7: RB1316.2, RB1317.1, RVO1306.1 (CCW)
XFF843136EDFC476A6FA7: R1319.2, R1320.1, U1312.5 (+)
