Takazudo/zudo-osc-hole-field/boards/osc-core/sheets/oscillator_O4_K.kicad_sch

## KiCad design boards/osc-core/sheets/oscillator_O4_K.kicad_sch (2026-10-05)

Schematic: oscillator_O4_K.kicad_sch

Parts:
C1401, C1403: 1e-10 F; C0603; MPN C0603C101J5GACTU
C1402, C1404: 1e-11 F; C0603
C1405, C1406, C1407: 1e-08 F; C0603
C1408, C1410, C1429, C1430, C1431, C1432, C1433, C1434, C1435, C1436, C1437, C1438, C1439, C1442, C1443, C1444, C1445, C1446, C1447, C1448, C1449: 100 nF; C0603; MPN GRM188R71H104KA93D
C1409: 100 pF; C0603; MPN C0603C101J5GACTU
C1411: 1 nF C0G; C0603
C1412: 10 nF; C0603
C1413, C1414, C1415, C1416, C1417, C1418, C1419, C1420: 1 nF; C0603
DO1405: BAT54S,215; SOT-23; MPN BAT54S,215
Q1401: BCM847BS,115; SOT-363_SC-70-6; MPN BCM847BS,115
R1417, R1423, R1448: 100 Ω; R0603
R1418, R1424, R1458: 10000 Ω; R0603
R1419, R1425, R1429, R1431, R1433: 1000 Ω; R0603
R1420, R1426, R1430, R1432, R1434: 1e+07 Ω; R0603
R1421, R1422, R1427, R1428, R1456: 100000 Ω; R0603; MPN RT0603BRD07100KL
R1435, R1490: 1 kΩ; R0603
R1436, R1439: 10 MΩ; R0603
R1437, R1476: 40 kΩ; R0603
R1438, R1440, R1441, R1445, R1461, R1463, R1466, R1469, R1470, R1472, R1475, R1477, R1479, R1481, R1482, R1483, R1484, R1485, R1487, R1488, R1495, R1496, R1497, R1498, R1499: 100 kΩ; R0603; MPN RT0603BRD07100KL
R1442, R1474: 250 kΩ; R0603
R1443: 5 MΩ; R0603
R1444, R1467: 200 kΩ; R0603
R1446: 82.5 kΩ; R0603
R1447, R1491: 1 MΩ; R0603
R1449, R1462, R1464, R1473, R1492, R1493, R1494: 10 kΩ; R0603
R1450: 24 kΩ; R0603
R1451: 5.72 kΩ; R0603
R1452: 1.5 kΩ; R0603
R1453: 1.2 MΩ; R0603
R1454: 470 Ω; R0603
R1455: 51 kΩ; R0603
R1457: 33200 Ω; R0603
R1459: 390000 Ω; R0603
R1460: 4700 Ω; R0603
R1465: 72 kΩ; R0603
R1468: 1.8 MΩ; R0603
R1471: 25 kΩ; R0603
R1478: 125 kΩ; R0603
R1480: 80 kΩ; R0603
R1486: 4.7 kΩ; R0603
R1489: 68 kΩ; R0603
RB1401: 49.9 kΩ; R0603
RB1410, RB1411, RB1412, RB1413, RB1414, RB1415, RB1416, RB1417, RB1418, RB1419, RB1420, RB1421: 100 Ω; R0603
RVO1406, RVO1407, RVO1410, RVO1411: 10 kΩ; Potentiometer_Bourns_TC33X_Vertical; MPN TC33X-2-103E
RVO1408: 1 kΩ; Potentiometer_Bourns_TC33X_Vertical; MPN TC33X-2-102E
RVO1409: 20 kΩ; Potentiometer_Bourns_TC33X_Vertical
U1405: AS3340D; SOIC-16_3.9x9.9mm_P1.27mm; MPN AS3340D
U1406, U1408: LM393BIDR; SOIC-8_3.9x4.9mm_P1.27mm; MPN LM393BIDR
U1407: SN74HC14DR; SOIC-14_3.9x8.7mm_P1.27mm; MPN SN74HC14DR
U1409, U1410, U1411: OPA4197IPWR; TSSOP-14_4.4x5mm_P0.65mm; MPN OPA4197IPWR; LCSC C2057327
U1412, U1413, U1414, U1415: OPA4196IDR; SOIC-14_3.9x8.7mm_P1.27mm; MPN OPA4196IDR; LCSC C2057385

Connections:
+5V: C1432.1, R1460.1, R1486.1, U1406.6 (-), U1407.14 (VCC), U1408.6 (-)
+12V: C1429.1, C1431.1, C1433.1, C1434.1, C1436.1, C1438.1, C1442.1, C1444.1, C1446.1, C1448.1, R1453.1, R1493.1, R1494.1, U1405.16 (VCC), U1406.8 (V+), U1408.8 (V+), U1409.4 (V+), U1410.4 (V+), U1411.4 (V+), U1412.4 (V+), U1413.4 (V+), U1414.4 (V+), U1415.4 (V+)
-12V: C1435.1, C1437.1, C1439.1, C1443.1, C1445.1, C1447.1, C1449.1, R1492.2, U1409.11 (V-), U1410.11 (V-), U1411.11 (V-), U1412.11 (V-), U1413.11 (V-), U1414.11 (V-), U1415.11 (V-)
AGND: C1405.2, C1406.2, C1407.2, C1408.2, C1410.2, C1411.2, C1412.2, C1429.2, C1430.2, C1431.2, C1432.2, C1433.2, C1434.2, C1435.2, C1436.2, C1437.2, C1438.2, C1439.2, C1442.2, C1443.2, C1444.2, C1445.2, C1446.2, C1447.2, C1448.2, C1449.2, DO1405.1 (A), Q1401.5 (B2), R1420.2, R1426.2, R1430.2, R1432.2, R1434.2, R1436.2, R1438.2, R1439.2, R1451.2, R1455.2, R1461.2, R1463.2, R1472.2, R1475.2, R1479.2, R1483.2, R1485.2, R1490.2, R1496.2, RVO1407.2 (Wiper), RVO1407.3 (CW), RVO1408.2 (Wiper), RVO1408.3 (CW), RVO1409.3 (CW), U1405.12 (GND), U1406.4 (GND), U1406.5 (+), U1407.3, U1407.5, U1407.7 (GND), U1407.9, U1407.11, U1407.13, U1408.4 (GND), U1408.5 (+), U1411.10 (+), U1411.12 (+), U1413.10 (+), U1413.12 (+), U1415.5 (+), U1415.10 (+), U1415.12 (+)
X0A690587C80EFD567FF7: R1477.1, R1489.1, U1414.7
X0B332CC3F3D75834394B: R1446.1, R1457.1, R1468.1, R1471.1, R1474.1, R1478.1, R1484.1, R1488.1, RB1410.2, RB1411.1
X0FACA99AD1C64873D358: C1404.2, R1427.2, R1428.2, U1412.13 (-)
X1A432F522042ECEC7C4B: R1495.2, R1496.1, U1415.3 (+)
X01E3A8129482739C6219: R1440.2, R1441.2, R1442.2, R1443.2, R1444.2, R1445.2, R1446.2, R1447.2, U1405.15 (VFCI)
X2AA3374E8678E9BA0A93: RB1401.2, RVO1411.1 (CCW)
X2CB33306AB46A8FB1B0C: C1406.1, R1431.2, R1432.1, U1409.5 (+)
X2CEF3D9360F36CEF3D64: C1401.1, R1417.1, U1412.1
X2DAE1746253A01B64F3C: R1423.2, R1424.1
X3A40E8EF8CF7F10E8B15: R1474.2, R1475.1, U1414.5 (+)
X3A91CAA7F25B51AB2B7B: R1443.1, U1409.6 (-), U1409.7
X3B6FB499E20187857C2B: R1441.1, U1409.8, U1409.9 (-)
X3E0F21BF8D9F13295ECB: R1499.2, RVO1411.2 (Wiper), RVO1411.3 (CW), U1415.6 (-)
X4B88CD34EACF13ACADCA: C1419.1, RB1418.1, U1411.1
X4D9690800E6BDB473824: R1453.2, R1454.1, RVO1409.2 (Wiper), U1405.13 (VLFI)
X5B1CFAEB1EE416C898FF: C1416.1, RB1412.1, U1410.7
X5B8B360EBF4F11DF3096: R1450.2, RVO1407.1 (CCW)
X5BC1C28EAF5D67603036: R1417.2, R1418.1
X5BE49425103F808B4B93: R1456.1
X5D363BBEA087A98270AF: C1408.1, R1435.2, R1436.1, U1409.10 (+)
X6A4B8EF46A80D98620E0: U1410.3 (+), U1410.10 (+), U1411.3 (+)
X6AC970015EC98F4426CA: C1403.1, R1423.1, U1412.8
X6CE24F05B87A422ADF17: R1471.2, R1472.1, U1414.3 (+)
X6D5A56540D673957805B: R1452.2, RVO1408.1 (CCW)
X6DE01BB60F3B72F8EF8F: R1466.1, U1413.1, U1413.2 (-)
X6EAC04CA06B0A7EECE2C: R1437.2, R1438.1, U1413.6 (-)
X7B6418A02124BE1D6A53: R1439.1, R1445.1
X7E656C5058DD2C35CC89: R1419.2, R1420.1, U1412.5 (+)
X7F796329AA4AAD63EB4A: Q1401.2 (B1), R1489.2, R1490.1, R1491.2
X7FF164FB414EE3E69E00: R1461.1, R1462.1
X08F1314797B3395E626D: C1417.2, RB1415.2, U1410.9 (-)
X8FC7B1817AD1084FE573: R1484.2, R1485.1, U1408.3 (+)
X9BD8657620FE7D590E17: R1480.2, R1481.2, U1414.9 (-)
X9D8F336BA752C392B015: C1411.1, U1405.11 (CAP)
X09F11B5FD91688775527: R1440.1
X13A749CF8930D999CF9D: C1416.2, RB1413.2, U1410.6 (-)
X28EC889F0C4CD762D061: RB1420.2, RB1421.1, RVO1410.1 (CCW)
X40C0F76AACA5D9EF113E: R1498.1, R1499.1, U1415.1
X51C50B1EB9FD615BD1EF: U1411.13 (-), U1411.14
X053E05A700F39A722C78: Q1401.6 (C1), R1493.2, R1497.1
X60EB5CC16BDEAD4EB87D: R1456.2, R1457.2, U1406.2 (-)
X61AA0EC574E2B0F1D43A: C1415.2, RB1411.2, U1410.2 (-)
X61C55F327009ADDFA763: U1407.2
X62F8CF08CD4AAC85D881: C1415.1, RB1410.1, U1410.1
X65AE667238FA95A8F74F: R1433.1
X68EABB1CDA58EEC16A1A: C1418.1, RB1416.1, U1410.14
X80AB923B405609CBD8D4: R1421.1, U1412.3 (+)
X81E4F7C2070FDB7DD133: C1413.2, U1405.9 (VSSI)
X88BE562810A4F10EE019: R1447.1, RVO1406.2 (Wiper)
X89FA9515372969F8D13C: R1458.1
X94F2DFF912BE788DE93C: R1476.1, U1405.10 (VTO)
X455EF32C35C4474BE38C: C1414.2, U1405.6 (VHSI)
X545BE4CF2456EC7A5F25: R1455.1, R1482.1, U1405.4 (VP)
X619CE288967320072B9E: R1442.1, U1409.1, U1409.2 (-)
X657FF93253181E495FDF: R1487.2, R1488.2, U1414.13 (-)
X831C044FF28F8040051D: C1420.1, RB1420.1, U1411.7
X895FBEC3FB8F4C2CEA5A: C1405.1, R1429.2, R1430.1, U1409.3 (+)
X3103A7AACC62E49A7020: U1415.8, U1415.9 (-)
X3380A93A6DFB5ED50C54: R1459.1, R1460.2, U1406.1, U1407.1
X5929B9536D17079BD5A9: RB1401.1, U1415.7
X5950FD1D82173B48B2DA: R1469.2, R1470.2, U1413.13 (-)
X6354D048E3F28D8D058A: R1487.1, U1414.14
X7355BCC8FF97C5BB91AE: RVO1409.1 (CCW), U1405.7 (VHFT)
X7618FDA4386E634844C4: R1458.2, R1459.2, U1406.3 (+)
X8155CFB345211D94E7E1: R1480.1, U1405.8 (VSO)
X8759D51172E1D22B97F8: U1411.8, U1411.9 (-)
X58561AA2E73699DE0EE0: Q1401.1 (E1), Q1401.4 (E2), R1492.1
X461891EDAD0B2EB306D7: R1437.1, U1413.7
X513965EE2097F51F0F25: R1478.2, R1479.1, U1414.10 (+)
X687677C0C9C9CD503E02: U1415.13 (-), U1415.14
X4675570B5E238C794F75: R1486.2, U1408.1, U1414.12 (+)
X7232057F47316092B5DF: R1431.1
X62232080C40C3946475B: R1435.1
X394087072DAEF9F4226C: U1410.5 (+), U1410.12 (+), U1411.5 (+)
XA8B41C5E783E930EABC9: R1476.2, R1477.2, U1414.6 (-)
XA10A4FD55CBA7C24DBD3: C1430.1, R1448.2, R1449.1, U1405.3 (VEE)
XA475C5A5C3A775FF851C: R1425.2, R1426.1, U1412.12 (+)
XAC8E39F8B82E205A502C: R1481.1, U1414.8
XAC76DAA63DA3CCD3B2A6: R1451.1, U1405.2 (SCALE2)
XAD4B84CEAD60B8EC35EB: RB1416.2, RB1417.1, RVO1406.1 (CCW)
XAE6DFF8BF73D9FECACD1: C1417.1, RB1414.1, U1410.8
XAFD7889E4E6A69543577: R1465.1, R1469.1, U1413.8
XB0C1756D21C6778D28FA: R1491.1, RVO1410.2 (Wiper)
XB0C6340C216F125DBC15: RB1414.2, RB1415.1, RVO1406.3 (CW)
XB9CA1657C3FE4A661A50: C1403.2, R1424.2, U1412.9 (-)
XB382FF2F29793C141C46: DO1405.2 (K), U1414.1, U1414.2 (-)
XB9659D0FE357D416179A: C1409.1, R1448.1, U1409.14
XBB8A52B6D120F7F84C27: R1465.2, R1466.2, R1467.2, R1468.2, U1413.9 (-)
XBC6D6D45B499021397AA: C1407.1, R1433.2, R1434.1, U1413.3 (+)
XBDA3123A09CE38CAF818: C1414.1, R1464.2
XBF56AE4CB459DBCA7D9D: R1482.2, R1483.1, U1408.2 (-)
XC23E48D870D5AC2D2A34: C1412.1, R1454.2
XC66CCAB52FC5254DE89B: C1409.2, R1449.2, U1409.13 (-)
XC88720F3206DF29BA827: DO1405.3 (COM), R1473.2, U1405.5 (VPWM)
XC2796892AE24D14CFF96: C1413.1, R1462.2
XCEE2A45C975E1AFE65D9: R1425.1
XD71A341469CB38F48F2E: RB1418.2, RB1419.1, RVO1410.3 (CW)
XD456DD827D89E30933BE: C1401.2, R1418.2, U1412.2 (-)
XD874630B23D22DC99F5A: C1419.2, RB1419.2, U1411.2 (-)
XDCA0B619EEB5CA3698FD: C1404.1, R1428.1, R1467.1, U1412.14
XDD3424A56BA0C1838507: R1427.1, U1412.10 (+)
XE43539C6CE833EF7B4F7: C1410.1, R1452.1, U1405.14 (VS)
XE791271B320998D9883D: C1418.2, RB1417.2, U1410.13 (-)
XEAD088C182B8309B371C: R1470.1, R1473.1, U1413.14
XEC29CCFBAB51F823DB99: R1419.1
XEEBF623F70AFAC681050: Q1401.3 (C2), R1494.2, R1495.1
XF5B9E6F0AF41CB8B8516: R1429.1
XF61D92A2B65A922BB2C4: R1450.1, U1405.1 (SCALE1)
XF2827D8A0A013B839CAA: RB1412.2, RB1413.1, U1409.12 (+), U1413.5 (+)
XF7228A65C6A9198C768F: R1497.2, R1498.2, U1415.2 (-)
XF43267DF1B146BFF5ECF: C1420.2, RB1421.2, U1411.6 (-)
XF03460370C0B4C26F1EA: C1402.2, R1421.2, R1422.2, U1412.6 (-)
XFA69D8EDE2A5B2C1520E: C1402.1, R1422.1, R1444.1, U1412.7
XFEC100AF3DB43E9BF8BD: R1463.1, R1464.1
