Takazudo/zudo-osc-hole-field/boards/osc-core/sheets/oscillator_O5_K.kicad_sch

## KiCad design boards/osc-core/sheets/oscillator_O5_K.kicad_sch (2026-10-05)

Schematic: oscillator_O5_K.kicad_sch

Parts:
C1501, C1503: 1e-10 F; C0603; MPN C0603C101J5GACTU
C1502, C1504: 1e-11 F; C0603
C1505, C1506, C1507: 1e-08 F; C0603
C1508, C1510, C1529, C1530, C1531, C1532, C1533, C1534, C1535, C1536, C1537, C1538, C1539, C1542, C1543, C1544, C1545, C1546, C1547, C1548, C1549: 100 nF; C0603; MPN GRM188R71H104KA93D
C1509: 100 pF; C0603; MPN C0603C101J5GACTU
C1511: 1 nF C0G; C0603
C1512: 10 nF; C0603
C1513, C1514, C1515, C1516, C1517, C1518, C1519, C1520: 1 nF; C0603
DO1505: BAT54S,215; SOT-23; MPN BAT54S,215
Q1501: BCM847BS,115; SOT-363_SC-70-6; MPN BCM847BS,115
R1517, R1523, R1548: 100 Ω; R0603
R1518, R1524, R1558: 10000 Ω; R0603
R1519, R1525, R1529, R1531, R1533: 1000 Ω; R0603
R1520, R1526, R1530, R1532, R1534: 1e+07 Ω; R0603
R1521, R1522, R1527, R1528, R1556: 100000 Ω; R0603; MPN RT0603BRD07100KL
R1535, R1590: 1 kΩ; R0603
R1536, R1539: 10 MΩ; R0603
R1537, R1576: 40 kΩ; R0603
R1538, R1540, R1541, R1545, R1561, R1563, R1566, R1569, R1570, R1572, R1575, R1577, R1579, R1581, R1582, R1583, R1584, R1585, R1587, R1588, R1595, R1596, R1597, R1598, R1599: 100 kΩ; R0603; MPN RT0603BRD07100KL
R1542, R1574: 250 kΩ; R0603
R1543: 5 MΩ; R0603
R1544, R1567: 200 kΩ; R0603
R1546: 82.5 kΩ; R0603
R1547, R1591: 1 MΩ; R0603
R1549, R1562, R1564, R1573, R1592, R1593, R1594: 10 kΩ; R0603
R1550: 24 kΩ; R0603
R1551: 5.72 kΩ; R0603
R1552: 1.5 kΩ; R0603
R1553: 1.2 MΩ; R0603
R1554: 470 Ω; R0603
R1555: 51 kΩ; R0603
R1557: 33200 Ω; R0603
R1559: 390000 Ω; R0603
R1560: 4700 Ω; R0603
R1565: 72 kΩ; R0603
R1568: 1.8 MΩ; R0603
R1571: 25 kΩ; R0603
R1578: 125 kΩ; R0603
R1580: 80 kΩ; R0603
R1586: 4.7 kΩ; R0603
R1589: 68 kΩ; R0603
RB1501: 49.9 kΩ; R0603
RB1510, RB1511, RB1512, RB1513, RB1514, RB1515, RB1516, RB1517, RB1518, RB1519, RB1520, RB1521: 100 Ω; R0603
RVO1506, RVO1507, RVO1510, RVO1511: 10 kΩ; Potentiometer_Bourns_TC33X_Vertical; MPN TC33X-2-103E
RVO1508: 1 kΩ; Potentiometer_Bourns_TC33X_Vertical; MPN TC33X-2-102E
RVO1509: 20 kΩ; Potentiometer_Bourns_TC33X_Vertical
U1505: AS3340D; SOIC-16_3.9x9.9mm_P1.27mm; MPN AS3340D
U1506, U1508: LM393BIDR; SOIC-8_3.9x4.9mm_P1.27mm; MPN LM393BIDR
U1507: SN74HC14DR; SOIC-14_3.9x8.7mm_P1.27mm; MPN SN74HC14DR
U1509, U1510, U1511: OPA4197IPWR; TSSOP-14_4.4x5mm_P0.65mm; MPN OPA4197IPWR; LCSC C2057327
U1512, U1513, U1514, U1515: OPA4196IDR; SOIC-14_3.9x8.7mm_P1.27mm; MPN OPA4196IDR; LCSC C2057385

Connections:
+5V: C1532.1, R1560.1, R1586.1, U1506.6 (-), U1507.14 (VCC), U1508.6 (-)
+12V: C1529.1, C1531.1, C1533.1, C1534.1, C1536.1, C1538.1, C1542.1, C1544.1, C1546.1, C1548.1, R1553.1, R1593.1, R1594.1, U1505.16 (VCC), U1506.8 (V+), U1508.8 (V+), U1509.4 (V+), U1510.4 (V+), U1511.4 (V+), U1512.4 (V+), U1513.4 (V+), U1514.4 (V+), U1515.4 (V+)
-12V: C1535.1, C1537.1, C1539.1, C1543.1, C1545.1, C1547.1, C1549.1, R1592.2, U1509.11 (V-), U1510.11 (V-), U1511.11 (V-), U1512.11 (V-), U1513.11 (V-), U1514.11 (V-), U1515.11 (V-)
AGND: C1505.2, C1506.2, C1507.2, C1508.2, C1510.2, C1511.2, C1512.2, C1529.2, C1530.2, C1531.2, C1532.2, C1533.2, C1534.2, C1535.2, C1536.2, C1537.2, C1538.2, C1539.2, C1542.2, C1543.2, C1544.2, C1545.2, C1546.2, C1547.2, C1548.2, C1549.2, DO1505.1 (A), Q1501.5 (B2), R1520.2, R1526.2, R1530.2, R1532.2, R1534.2, R1536.2, R1538.2, R1539.2, R1551.2, R1555.2, R1561.2, R1563.2, R1572.2, R1575.2, R1579.2, R1583.2, R1585.2, R1590.2, R1596.2, RVO1507.2 (Wiper), RVO1507.3 (CW), RVO1508.2 (Wiper), RVO1508.3 (CW), RVO1509.3 (CW), U1505.12 (GND), U1506.4 (GND), U1506.5 (+), U1507.3, U1507.5, U1507.7 (GND), U1507.9, U1507.11, U1507.13, U1508.4 (GND), U1508.5 (+), U1511.10 (+), U1511.12 (+), U1513.10 (+), U1513.12 (+), U1515.5 (+), U1515.10 (+), U1515.12 (+)
X1A3A22F4B289D6F62B00: R1527.1, U1512.10 (+)
X1DA464D505A944A51104: R1523.2, R1524.1
X1EFA117C7EEF218820F2: DO1505.2 (K), U1514.1, U1514.2 (-)
X2CAA5D9EBDF3ED4F13BF: R1542.1, U1509.1, U1509.2 (-)
X2D56A699CAA36B2F8F70: C1513.2, U1505.9 (VSSI)
X2F4053E8598569E6249E: U1507.2
X3A008FCE9861428924F4: C1511.1, U1505.11 (CAP)
X3DDBDA73F5D56EFA4F0B: R1574.2, R1575.1, U1514.5 (+)
X3FA0847880480FCD8CA8: Q1501.6 (C1), R1593.2, R1597.1
X4A2893F51D217C421EB0: U1515.8, U1515.9 (-)
X4C5B9D1927F731909366: R1547.1, RVO1506.2 (Wiper)
X5A5D1C8EBFCE84682A63: R1543.1, U1509.6 (-), U1509.7
X5B55A89E38A2C7BFC91F: C1517.2, RB1515.2, U1510.9 (-)
X5C8647167DDC35E8D571: R1550.1, U1505.1 (SCALE1)
X5E3DB5A6EE8A8094A2C0: C1506.1, R1531.2, R1532.1, U1509.5 (+)
X6A4B8EF46A80D98620E0: U1510.3 (+), U1510.10 (+), U1511.3 (+)
X6A4E9EB656E3E839FC9F: R1556.1
X6B246CF9F911B341A8E7: R1556.2, R1557.2, U1506.2 (-)
X6CD7D40085B2AA875B95: C1501.1, R1517.1, U1512.1
X6E8E4EF00B0B36A9BBA0: RB1514.2, RB1515.1, RVO1506.3 (CW)
X6EDA10396D557ACEB00C: R1569.2, R1570.2, U1513.13 (-)
X7CC5966245686CF4EF46: R1540.1
X8C7A5B7CE9F72C6F7AE4: R1559.1, R1560.2, U1506.1, U1507.1
X8FBC6CE4B9068F29759F: C1512.1, R1554.2
X9A3AD0A09F992B08B705: U1511.8, U1511.9 (-)
X9B7003267CE3618D16C7: C1502.2, R1521.2, R1522.2, U1512.6 (-)
X18EA476A6A2218FDAFC7: R1570.1, R1573.1, U1513.14
X19B12FE5B5BFA82ED4EF: C1508.1, R1535.2, R1536.1, U1509.10 (+)
X20E5F5A8A70133CE0A4F: R1577.1, R1589.1, U1514.7
X28D02EC85303873CBFC1: C1501.2, R1518.2, U1512.2 (-)
X31D32736C26AEE368EC7: R1552.2, RVO1508.1 (CCW)
X33ADBEB2EBFF18372234: R1565.2, R1566.2, R1567.2, R1568.2, U1513.9 (-)
X35E86F1B470C2BA578A1: R1517.2, R1518.1
X41EAA339E43383519D02: C1520.1, RB1520.1, U1511.7
X45CD497C677421FCA88D: R1551.1, U1505.2 (SCALE2)
X46F500A6E2D8313AC04C: RVO1509.1 (CCW), U1505.7 (VHFT)
X54B767EE3EF15D42FCDB: RB1518.2, RB1519.1, RVO1510.3 (CW)
X62A2707EE8FA5460FB50: RB1516.2, RB1517.1, RVO1506.1 (CCW)
X67C37D0B97255E3C9204: R1584.2, R1585.1, U1508.3 (+)
X78D1CF7F6D36BF7E68A7: R1576.1, U1505.10 (VTO)
X83EBE650C373FC40F1A9: C1509.2, R1549.2, U1509.13 (-)
X89FA9515372969F8D13C: R1558.1
X92B664FE8D6E6BD67D20: C1515.2, RB1511.2, U1510.2 (-)
X144C922A18FA87072963: R1519.1
X146B2E086CDC142CF6D6: R1563.1, R1564.1
X216FFA2B72BFD2E147BB: C1505.1, R1529.2, R1530.1, U1509.3 (+)
X392AC41CFD17951B15DD: R1550.2, RVO1507.1 (CCW)
X415A98876075354EE128: C1510.1, R1552.1, U1505.14 (VS)
X433FD126F86C14646F6B: R1558.2, R1559.2, U1506.3 (+)
X534FA7ABB4E26652B0FC: C1519.1, RB1518.1, U1511.1
X640C8F62DB4DCCB0BAC5: R1578.2, R1579.1, U1514.10 (+)
X785D66F7BC85D810667E: R1582.2, R1583.1, U1508.2 (-)
X798D878515D73FEB54E2: C1516.2, RB1513.2, U1510.6 (-)
X921E5F960C492F6391B9: C1507.1, R1533.2, R1534.1, U1513.3 (+)
X999D51C2C38750EE9CDB: C1502.1, R1522.1, R1544.1, U1512.7
X3043B48FC5CF33D29302: C1503.2, R1524.2, U1512.9 (-)
X4061D7D91D6A9735804B: RB1520.2, RB1521.1, RVO1510.1 (CCW)
X4838A855AA88CEFB49D1: R1531.1
X5768B5A3D3AC9B88DB51: R1533.1
X7753A9CB9C4C99AFEC62: R1521.1, U1512.3 (+)
X07912CCBA89494305A5E: C1518.2, RB1517.2, U1510.13 (-)
X023930B00833904F4737: C1530.1, R1548.2, R1549.1, U1505.3 (VEE)
X35174C84B94A00C322C5: C1516.1, RB1512.1, U1510.7
X50598DC0C3D8C362685E: RB1512.2, RB1513.1, U1509.12 (+), U1513.5 (+)
X72213A24DE56FD86B8A2: Q1501.2 (B1), R1589.2, R1590.1, R1591.2
X511868EB62E33CD36C02: R1555.1, R1582.1, U1505.4 (VP)
X570616CB52B08D70FD0C: R1535.1
X659082F58B27912CFAEF: C1509.1, R1548.1, U1509.14
X684243D2A276DABD886C: R1595.2, R1596.1, U1515.3 (+)
X921836E1517A72C27BFD: R1591.1, RVO1510.2 (Wiper)
X82199762F3EEFE7DE14F: U1515.13 (-), U1515.14
X394087072DAEF9F4226C: U1510.5 (+), U1510.12 (+), U1511.5 (+)
XA4C600E3067083BE8D5D: C1504.2, R1527.2, R1528.2, U1512.13 (-)
XA71DC16E64E8E667E1BE: C1519.2, RB1519.2, U1511.2 (-)
XA96E8D0F184A39DEE620: R1529.1
XAA1E6128AA3630183E80: R1576.2, R1577.2, U1514.6 (-)
XAEE7FCACA660B3CBC923: R1580.2, R1581.2, U1514.9 (-)
XB2DD4D7EC49EEE74C5CD: R1541.1, U1509.8, U1509.9 (-)
XB4CD63C81AA087A72AB4: C1520.2, RB1521.2, U1511.6 (-)
XB6D993FD2F5D67C1F525: Q1501.3 (C2), R1594.2, R1595.1
XB71E7B710EB023CD0E10: DO1505.3 (COM), R1573.2, U1505.5 (VPWM)
XB1740D19174FCDC57A89: R1537.1, U1513.7
XBE98C64E37574FAA5054: R1525.1
XC02642C739F5BF7A69ED: R1598.1, R1599.1, U1515.1
XD5D7C8886E3459F1E03A: R1519.2, R1520.1, U1512.5 (+)
XD6A7759380341409A047: R1537.2, R1538.1, U1513.6 (-)
XD723DD64A81EBCADFE5A: R1586.2, U1508.1, U1514.12 (+)
XDA57606F4A8A58CBDA77: C1514.1, R1564.2
XDCCA587447EF436FA48E: RB1501.2, RVO1511.1 (CCW)
XDE3151BBD80B06C87B09: R1580.1, U1505.8 (VSO)
XDEFB3A9091FCD4497A03: C1517.1, RB1514.1, U1510.8
XE0D36C507D9C0250C0B8: C1518.1, RB1516.1, U1510.14
XE31F7C2946B9C92B2BD4: R1587.2, R1588.2, U1514.13 (-)
XE53E68F96134553749FD: R1539.1, R1545.1
XE73D7BBF1230ECDCED27: C1513.1, R1562.2
XE779E0163B1C90616ED0: R1587.1, U1514.14
XE5186E13C39FD41C302C: R1581.1, U1514.8
XE5866228E5A533B6E0A9: R1561.1, R1562.1
XEA71DBF9A3F5D1DD1ED4: R1546.1, R1557.1, R1568.1, R1571.1, R1574.1, R1578.1, R1584.1, R1588.1, RB1510.2, RB1511.1
XEAE5C67212C77D34E57F: C1503.1, R1523.1, U1512.8
XEEDCBB302F5FFD2B09D0: R1597.2, R1598.2, U1515.2 (-)
XF2EFD6F1FD0527EFF713: R1571.2, R1572.1, U1514.3 (+)
XF6E8CFFDF6A4A9FA1EED: R1525.2, R1526.1, U1512.12 (+)
XF6F7C5A5FD2983B229DB: U1511.13 (-), U1511.14
XF84B9CFDCAF3BC8EB63D: R1566.1, U1513.1, U1513.2 (-)
XF785BFE6DF6F90409592: RB1501.1, U1515.7
XF1281ADC40D8EB606CE5: R1565.1, R1569.1, U1513.8
XF3837AC15B57FED870D5: C1504.1, R1528.1, R1567.1, U1512.14
XFA4EC43404E69F49DF74: C1514.2, U1505.6 (VHSI)
XFBB77182E7A1D927C8DA: R1599.2, RVO1511.2 (Wiper), RVO1511.3 (CW), U1515.6 (-)
XFD8EB31DB7BF2B1510E3: Q1501.1 (E1), Q1501.4 (E2), R1592.1
XFF25EE86908887869B5B: R1553.2, R1554.1, RVO1509.2 (Wiper), U1505.13 (VLFI)
XFF191EBF9D7844BA13A5: C1515.1, RB1510.1, U1510.1
XFFE833AC13BBA6E534F5: R1540.2, R1541.2, R1542.2, R1543.2, R1544.2, R1545.2, R1546.2, R1547.2, U1505.15 (VFCI)
