Takazudo/zudo-osc-hole-field/boards/osc-core/sheets/sample_hold_H1_K.kicad_sch

## KiCad design boards/osc-core/sheets/sample_hold_H1_K.kicad_sch (2026-10-05)

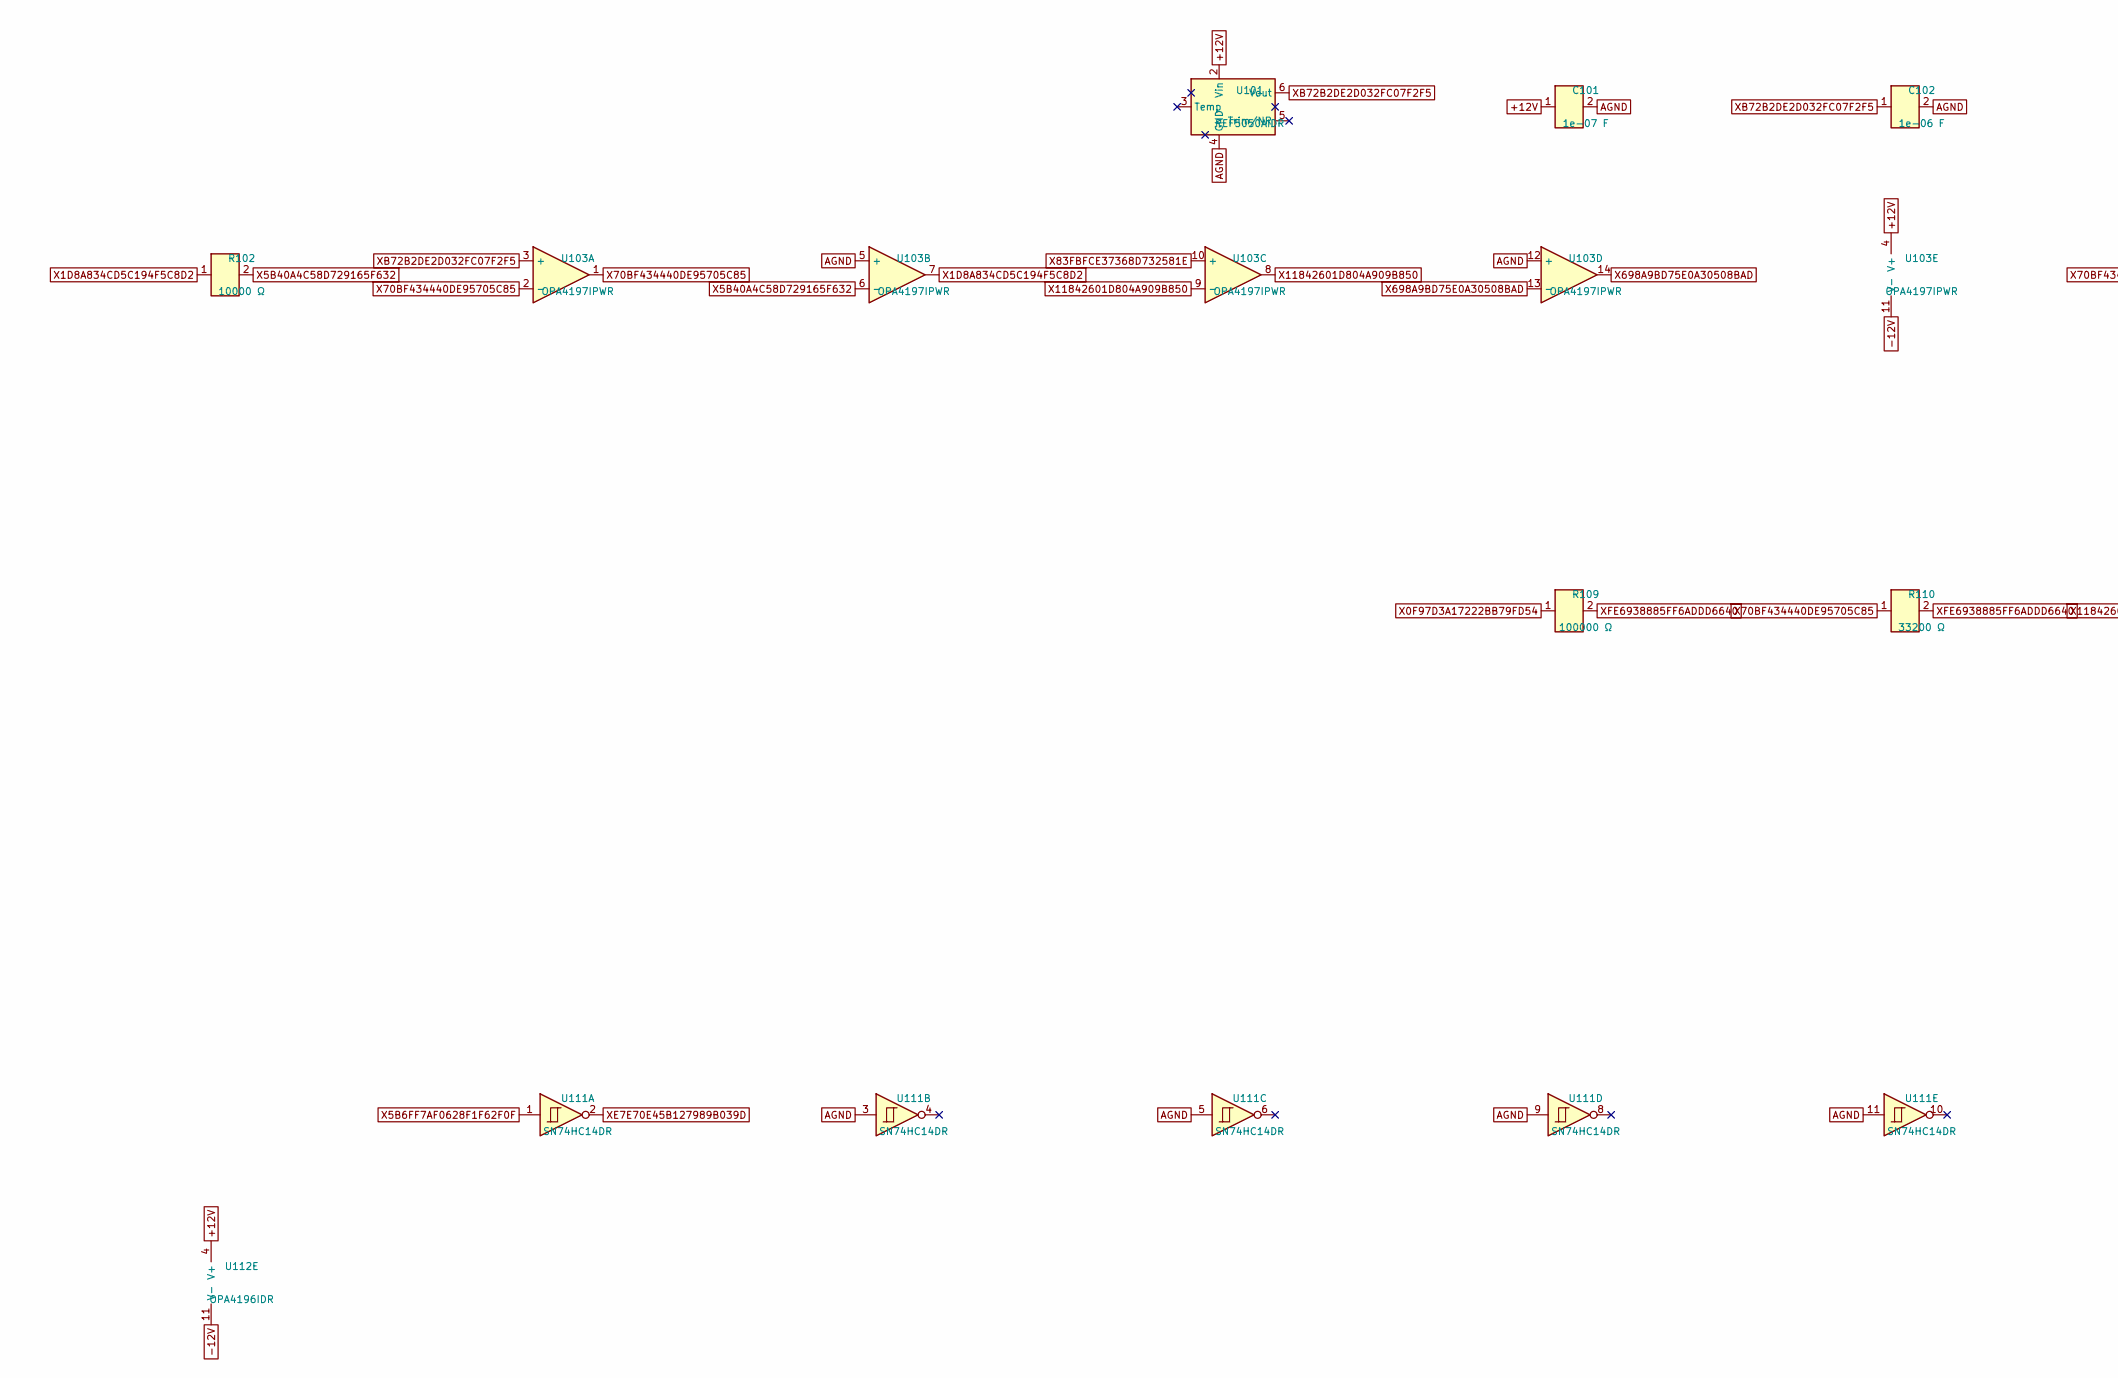
[picture p179: schematic sample_hold_H1_K.kicad_sch, part in row 1, column 1]

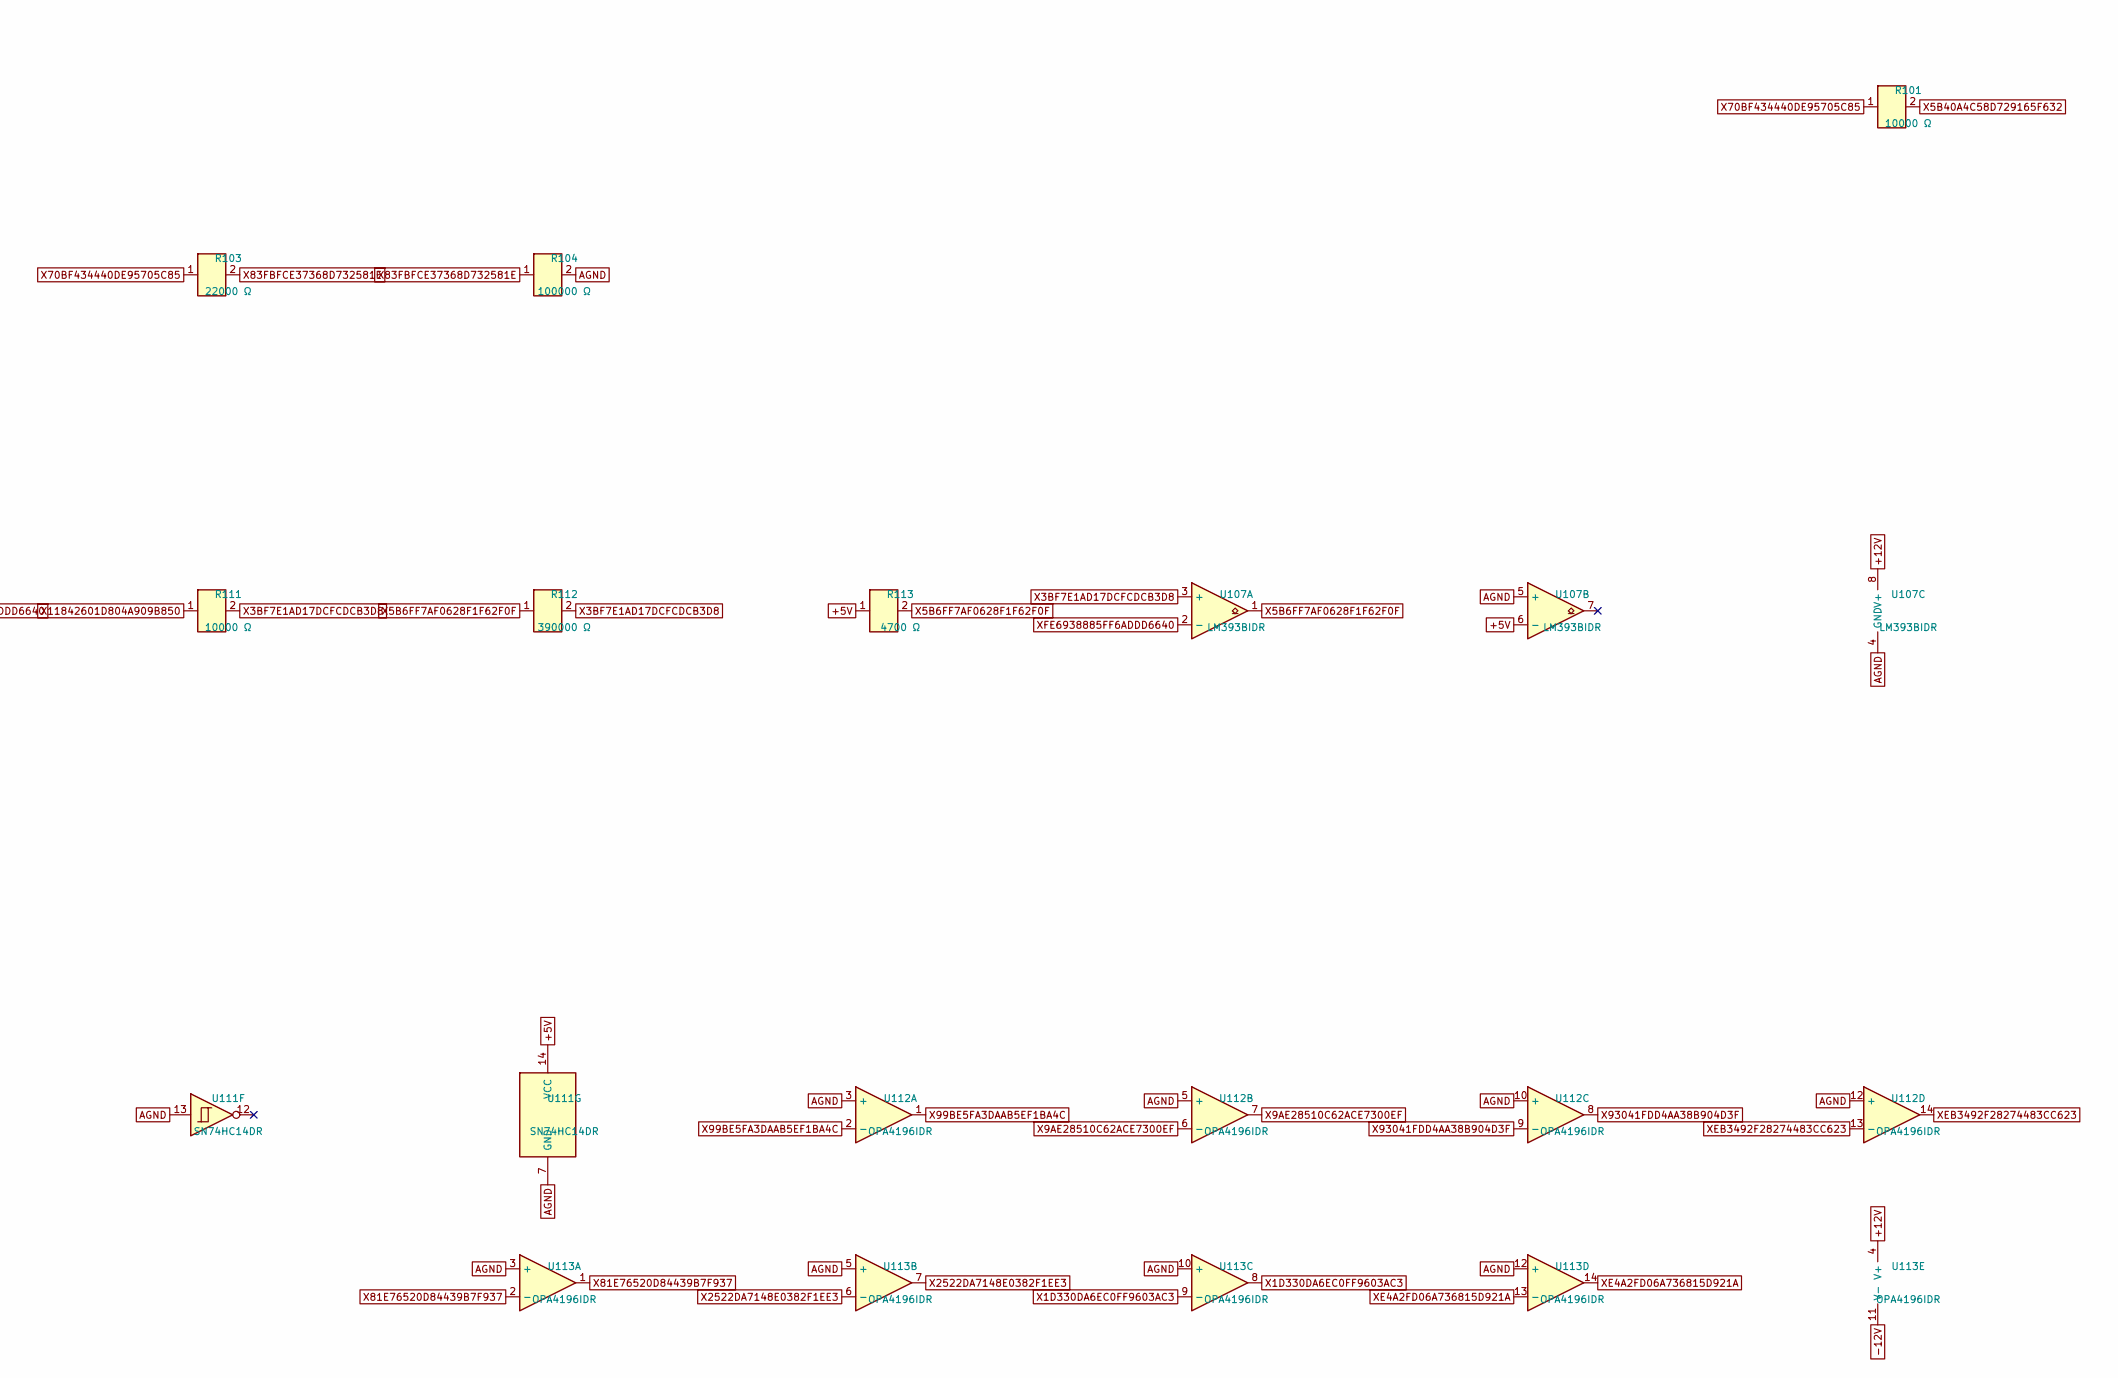
[picture p180: schematic sample_hold_H1_K.kicad_sch, part in row 1, column 2]

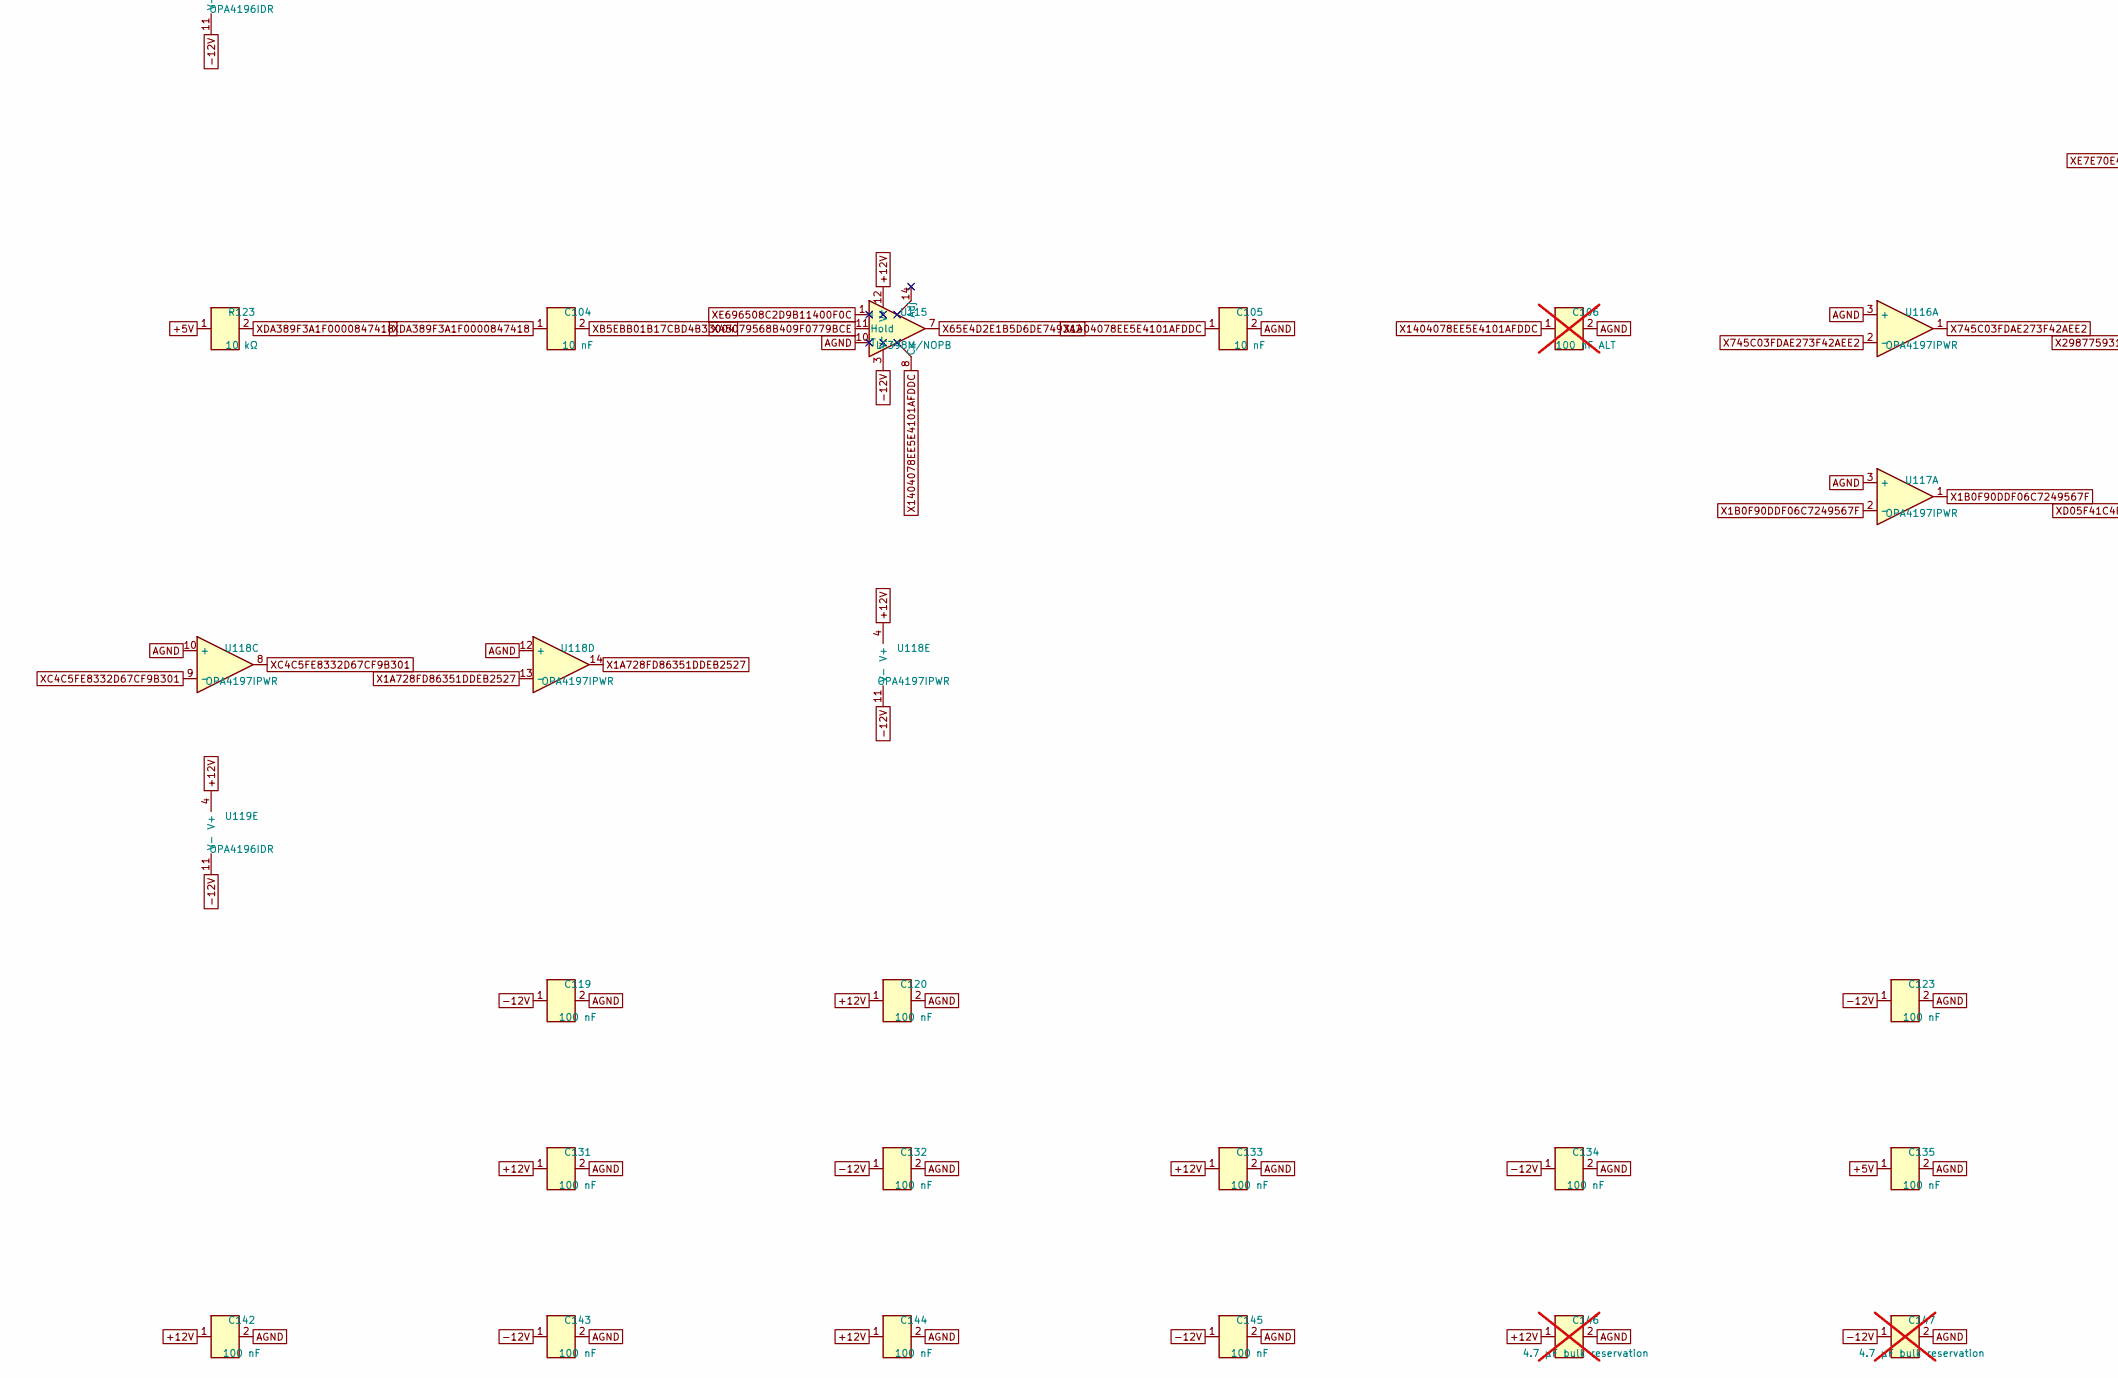
[picture p181: schematic sample_hold_H1_K.kicad_sch, part in row 2, column 1]

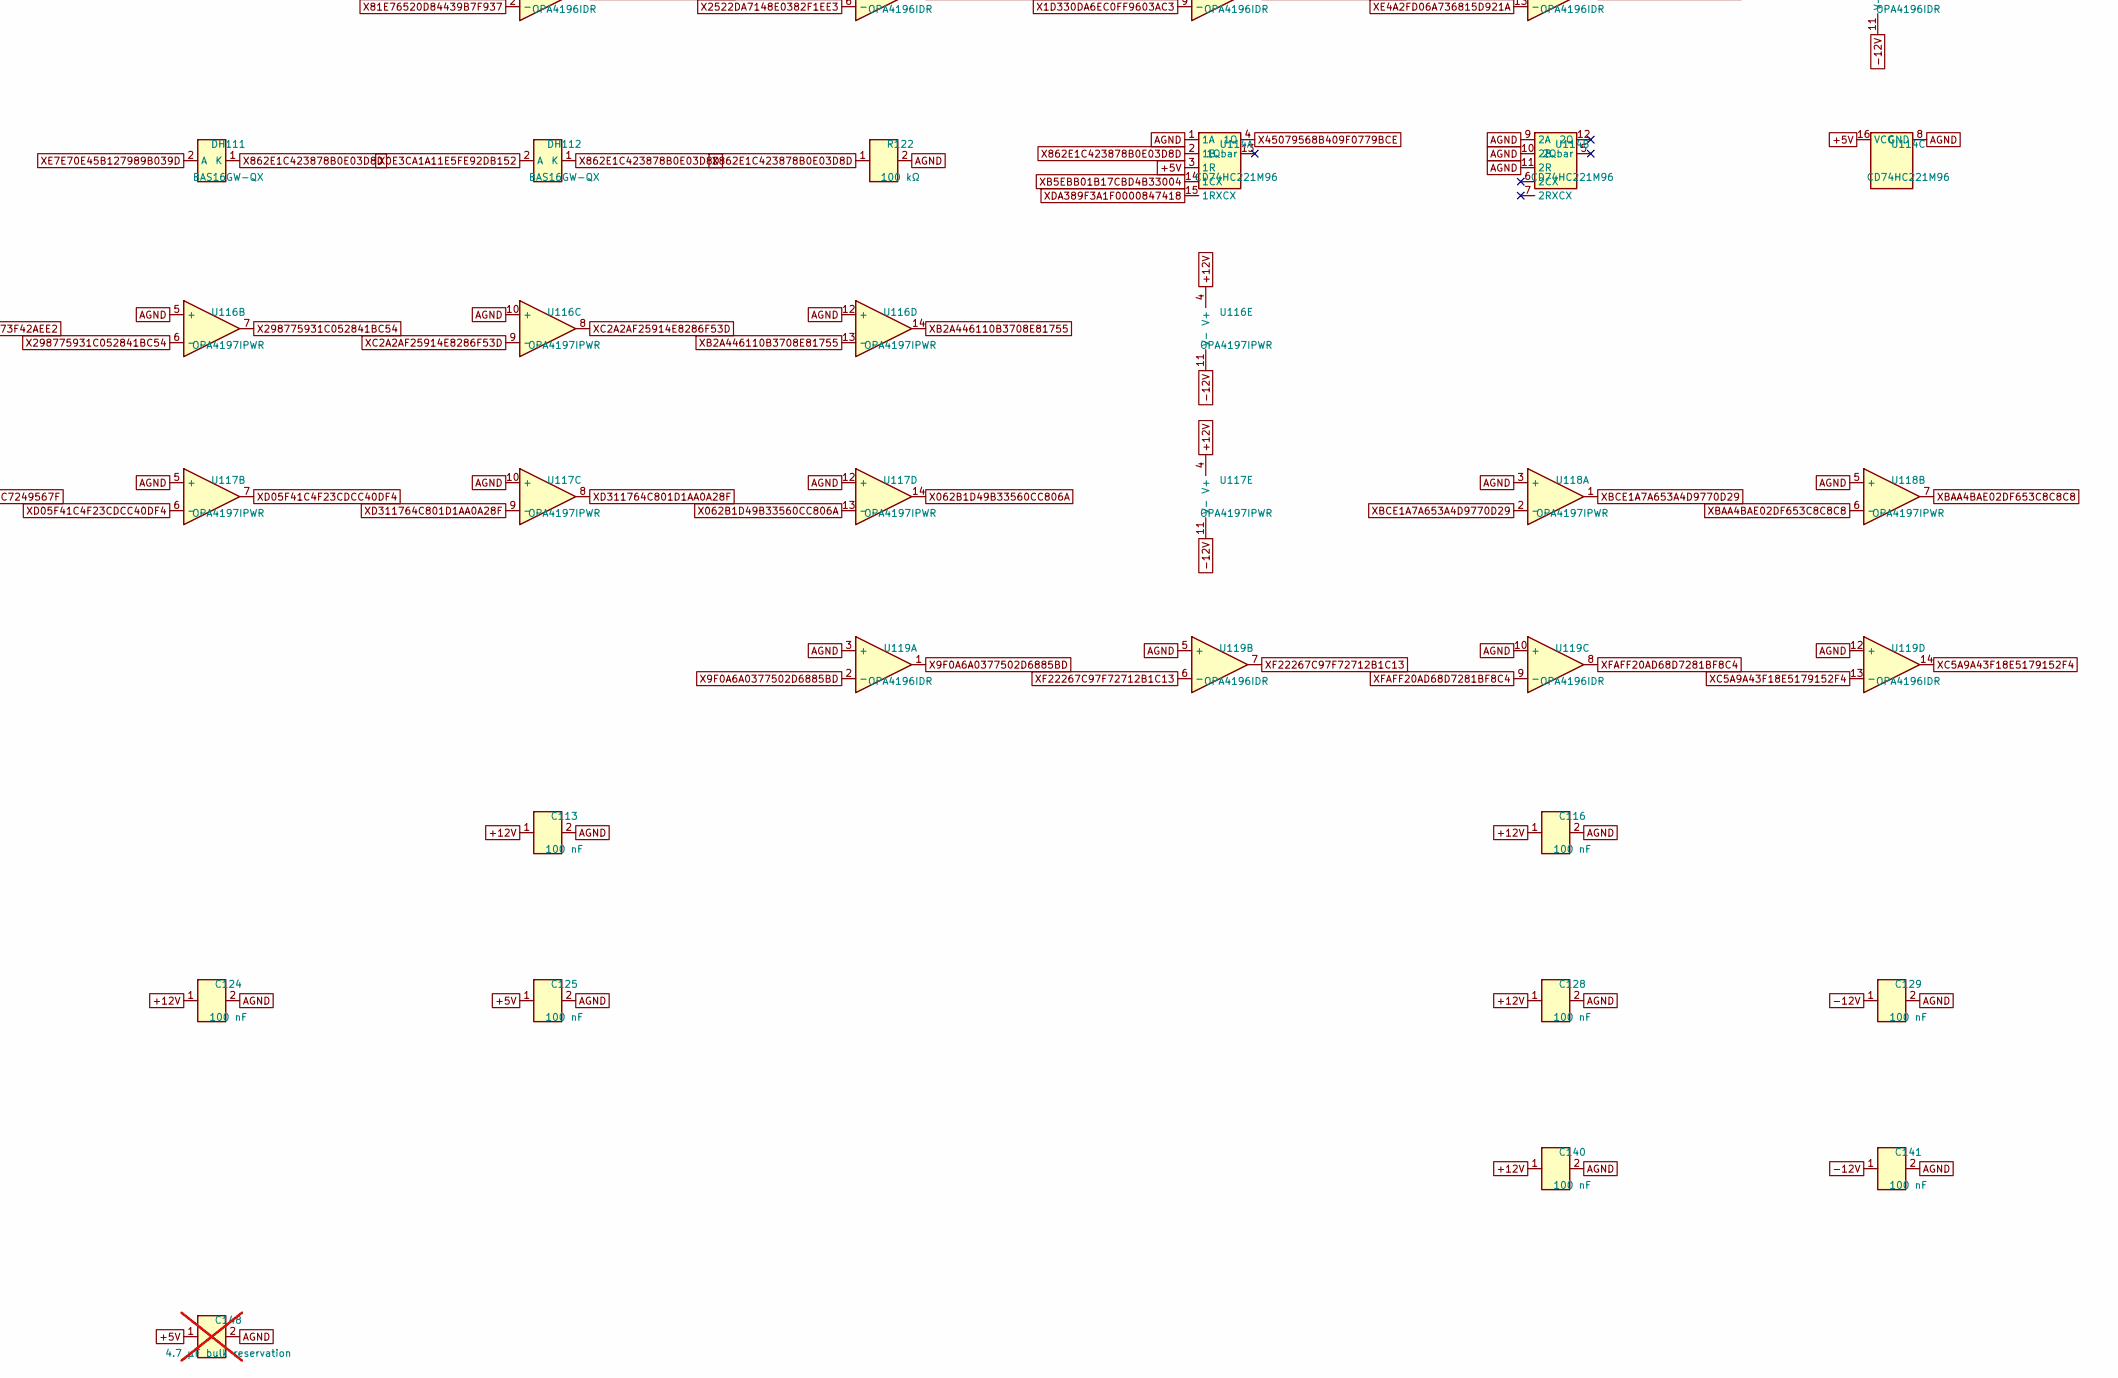
[picture p182: schematic sample_hold_H1_K.kicad_sch, part in row 2, column 2]

Parts:
C101: 1e-07 F; C0603; MPN GRM188R71H104KA93D
C102: 1e-06 F; C0603
C104, C105: 10 nF; C0805; MPN C0805C103J5GACTU; LCSC C2167597
C106: 100 nF ALT; C0805; not fitted
C113, C116, C119, C120, C123, C124, C125, C128, C129, C131, C132, C133, C134, C135, C140, C141, C142, C143, C144, C145: 100 nF; C0603; MPN GRM188R71H104KA93D
C146, C147, C148: 4.7 µF bulk reservation; C0805; MPN GRM21BR61E475KA12L; not fitted
DH111, DH112: BAS16GW-QX; SOD-123; MPN BAS16GW-QX
R101, R102, R111: 10000 Ω; R0603
R103: 22000 Ω; R0603
R104, R109: 100000 Ω; R0603; MPN RT0603BRD07100KL
R110: 33200 Ω; R0603
R112: 390000 Ω; R0603
R113: 4700 Ω; R0603
R122: 100 kΩ; R0603; MPN RC0603FR-07100KL
R123: 10 kΩ; R0603
U101: REF5050AIDR; SOIC-8_3.9x4.9mm_P1.27mm; MPN REF5050AIDR; LCSC C27804
U103, U116, U117, U118: OPA4197IPWR; TSSOP-14_4.4x5mm_P0.65mm; MPN OPA4197IPWR; LCSC C2057327
U107: LM393BIDR; SOIC-8_3.9x4.9mm_P1.27mm; MPN LM393BIDR
U111: SN74HC14DR; SOIC-14_3.9x8.7mm_P1.27mm; MPN SN74HC14DR
U112, U113, U119: OPA4196IDR; SOIC-14_3.9x8.7mm_P1.27mm; MPN OPA4196IDR; LCSC C2057385
U114: CD74HC221M96; SOIC-16_3.9x9.9mm_P1.27mm; MPN CD74HC221M96; LCSC C133954
U115: LF398M/NOPB; SOIC-14_3.9x8.7mm_P1.27mm; MPN LF398M/NOPB; LCSC C1346172

Connections:
+5V: C125.1, C135.1, C148.1, R113.1, R123.1, U107.6 (-), U111.14 (VCC), U114.3 (1R), U114.16 (VCC)
+12V: C101.1, C113.1, C116.1, C120.1, C124.1, C128.1, C131.1, C133.1, C140.1, C142.1, C144.1, C146.1, U101.2 (Vin), U103.4 (V+), U107.8 (V+), U112.4 (V+), U113.4 (V+), U115.12 (V^{+}), U116.4 (V+), U117.4 (V+), U118.4 (V+), U119.4 (V+)
-12V: C119.1, C123.1, C129.1, C132.1, C134.1, C141.1, C143.1, C145.1, C147.1, U103.11 (V-), U112.11 (V-), U113.11 (V-), U115.3 (V^{-}), U116.11 (V-), U117.11 (V-), U118.11 (V-), U119.11 (V-)
AGND: C101.2, C102.2, C105.2, C106.2, C113.2, C116.2, C119.2, C120.2, C123.2, C124.2, C125.2, C128.2, C129.2, C131.2, C132.2, C133.2, C134.2, C135.2, C140.2, C141.2, C142.2, C143.2, C144.2, C145.2, C146.2, C147.2, C148.2, R104.2, R122.2, U101.4 (GND), U103.5 (+), U103.12 (+), U107.4 (GND), U107.5 (+), U111.3, U111.5, U111.7 (GND), U111.9, U111.11, U111.13, U112.3 (+), U112.5 (+), U112.10 (+), U112.12 (+), U113.3 (+), U113.5 (+), U113.10 (+), U113.12 (+), U114.1 (1A), U114.8 (GND), U114.9 (2A), U114.10 (2B), U114.11 (2R), U115.10 (T), U116.3 (+), U116.5 (+), U116.10 (+), U116.12 (+), U117.3 (+), U117.5 (+), U117.10 (+), U117.12 (+), U118.3 (+), U118.5 (+), U118.10 (+), U118.12 (+), U119.3 (+), U119.5 (+), U119.10 (+), U119.12 (+)
X0E3CA1A11E5FE92DB152: DH112.2 (A)
X0F97D3A17222BB79FD54: R109.1
X1A728FD86351DDEB2527: U118.13 (-), U118.14
X1B0F90DDF06C7249567F: U117.1, U117.2 (-)
X1D8A834CD5C194F5C8D2: R102.1, U103.7
X1D330DA6EC0FF9603AC3: U113.8, U113.9 (-)
X3BF7E1AD17DCFCDCB3D8: R111.2, R112.2, U107.3 (+)
X5B6FF7AF0628F1F62F0F: R112.1, R113.2, U107.1, U111.1
X5B40A4C58D729165F632: R101.2, R102.2, U103.6 (-)
X9AE28510C62ACE7300EF: U112.6 (-), U112.7
X9F0A6A0377502D6885BD: U119.1, U119.2 (-)
X062B1D49B33560CC806A: U117.13 (-), U117.14
X65E4D2E1B5D6DE7493A2: U115.7
X70BF434440DE95705C85: R101.1, R103.1, R110.1, U103.1, U103.2 (-)
X81E76520D84439B7F937: U113.1, U113.2 (-)
X83FBFCE37368D732581E: R103.2, R104.1, U103.10 (+)
X99BE5FA3DAAB5EF1BA4C: U112.1, U112.2 (-)
X698A9BD75E0A30508BAD: U103.13 (-), U103.14
X745C03FDAE273F42AEE2: U116.1, U116.2 (-)
X862E1C423878B0E03D8D: DH111.1 (K), DH112.1 (K), R122.1, U114.2 (1B)
X2522DA7148E0382F1EE3: U113.6 (-), U113.7
X93041FDD4AA38B904D3F: U112.8, U112.9 (-)
X1404078EE5E4101AFDDC: C105.1, C106.1, U115.8 (C_{h})
X11842601D804A909B850: R111.1, U103.8, U103.9 (-)
X45079568B409F0779BCE: U114.4 (1Q), U115.11 (Hold)
X298775931C052841BC54: U116.6 (-), U116.7
XB2A446110B3708E81755: U116.13 (-), U116.14
XB5EBB01B17CBD4B33004: C104.2, U114.14 (1CX)
XB72B2DE2D032FC07F2F5: C102.1, U101.6 (Vout), U103.3 (+)
XBAA4BAE02DF653C8C8C8: U118.6 (-), U118.7
XBCE1A7A653A4D9770D29: U118.1, U118.2 (-)
XC2A2AF25914E8286F53D: U116.8, U116.9 (-)
XC4C5FE8332D67CF9B301: U118.8, U118.9 (-)
XC5A9A43F18E5179152F4: U119.13 (-), U119.14
XD05F41C4F23CDCC40DF4: U117.6 (-), U117.7
XD311764C801D1AA0A28F: U117.8, U117.9 (-)
XDA389F3A1F0000847418: C104.1, R123.2, U114.15 (1RXCX)
XE4A2FD06A736815D921A: U113.13 (-), U113.14
XE7E70E45B127989B039D: DH111.2 (A), U111.2
XE696508C2D9B11400F0C: U115.1 (I)
XEB3492F28274483CC623: U112.13 (-), U112.14
XF22267C97F72712B1C13: U119.6 (-), U119.7
XFAFF20AD68D7281BF8C4: U119.8, U119.9 (-)
XFE6938885FF6ADDD6640: R109.2, R110.2, U107.2 (-)
