Takazudo/zudo-osc-hole-field/boards/osc-core/sheets/sample_hold_H2_K.kicad_sch

## KiCad design boards/osc-core/sheets/sample_hold_H2_K.kicad_sch (2026-10-05)

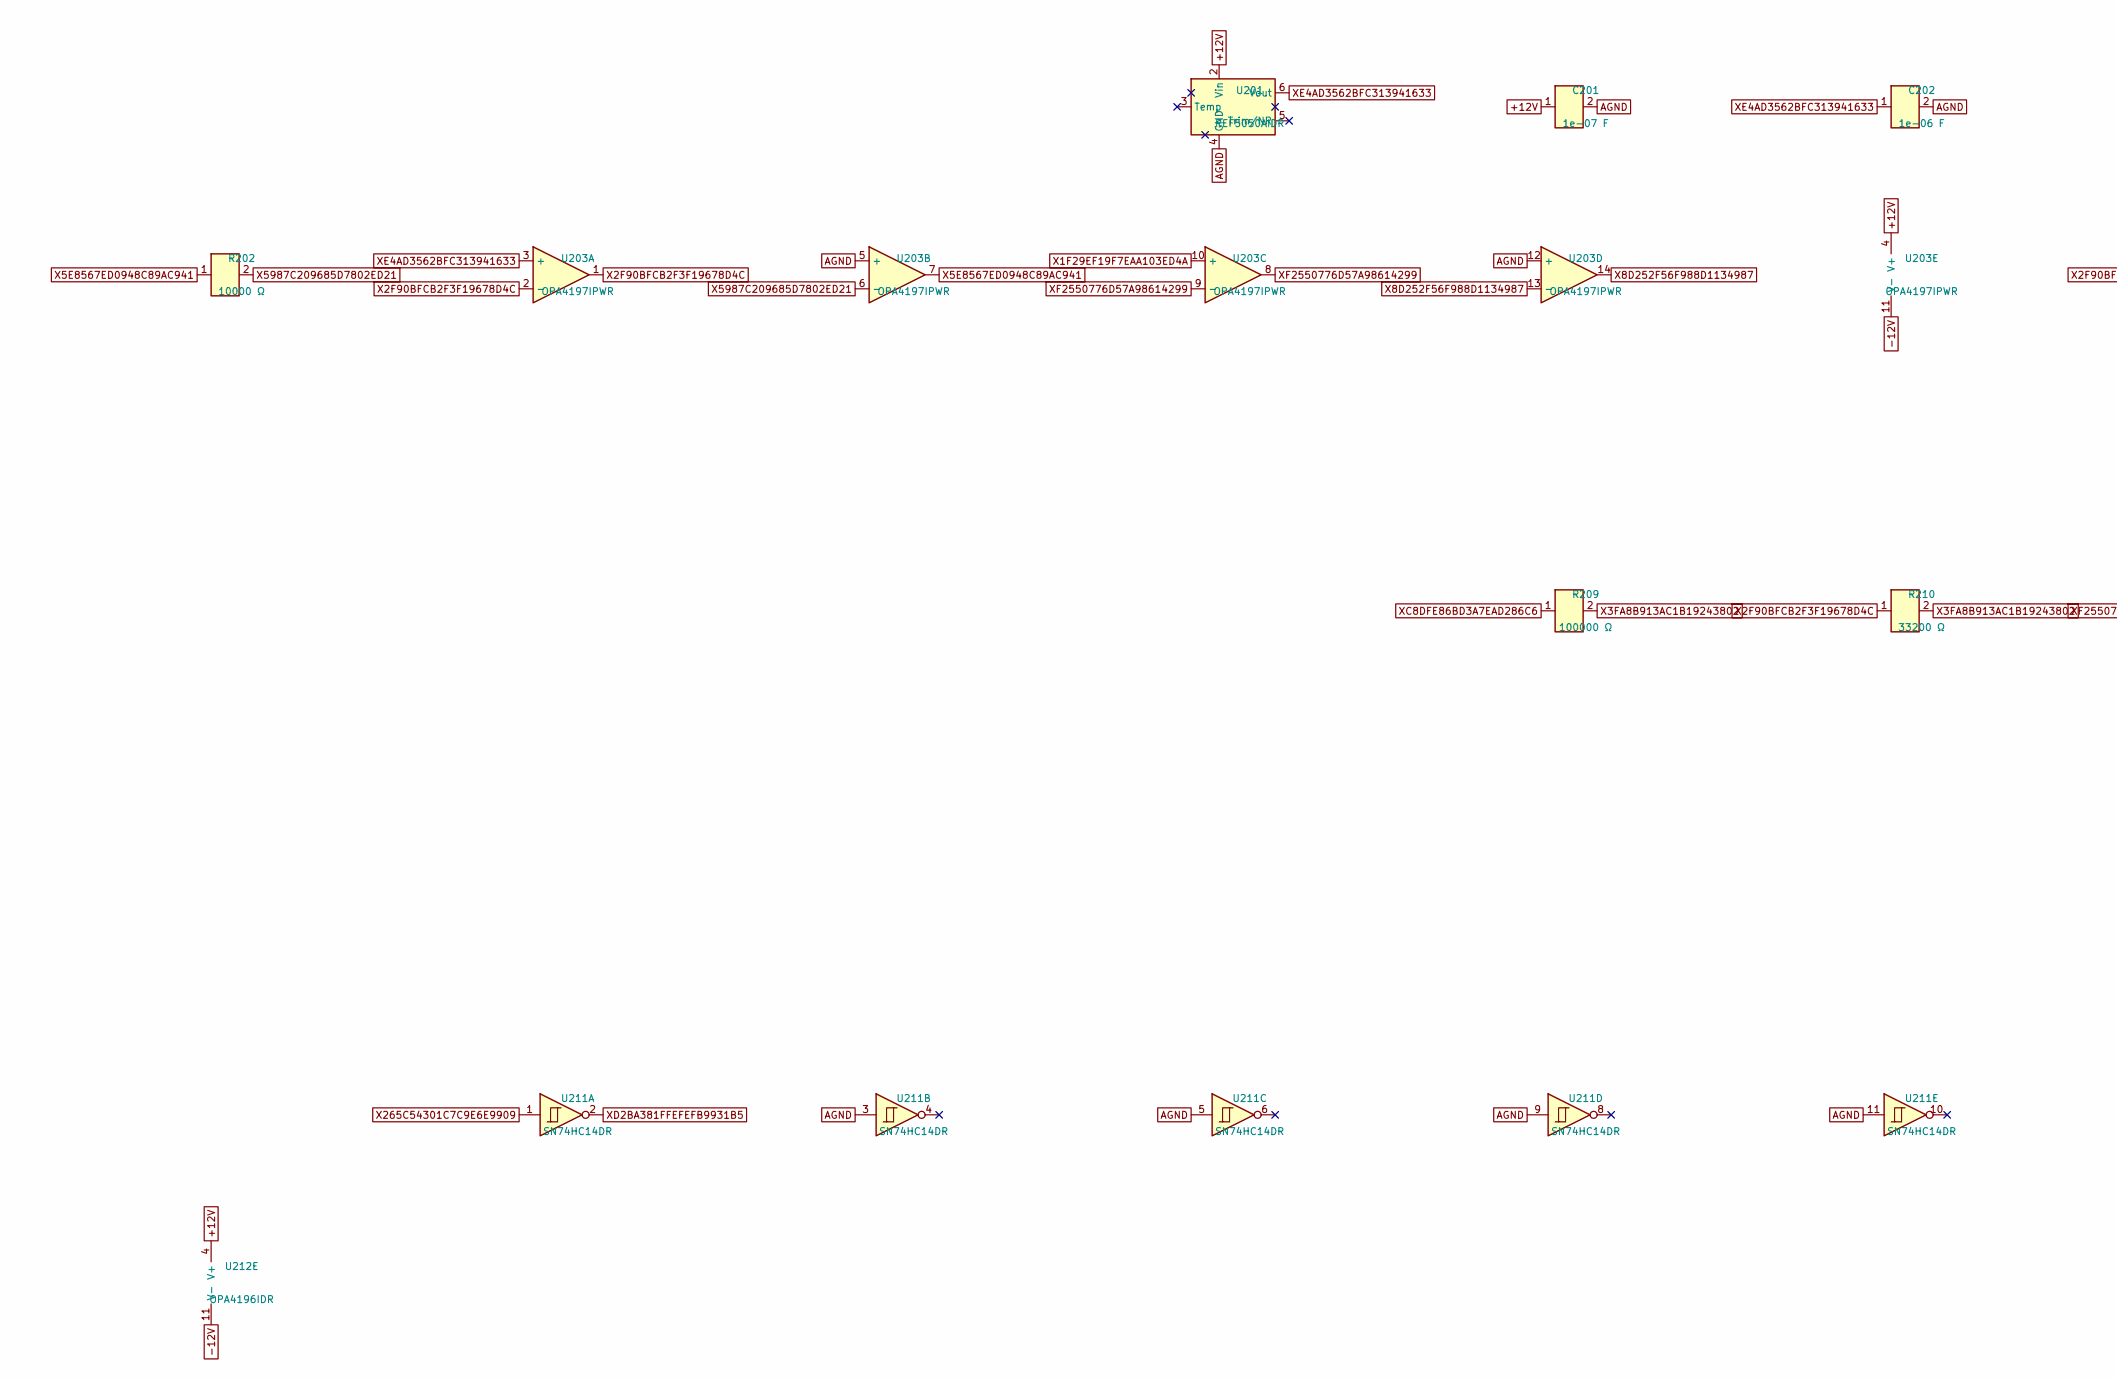
[picture p183: schematic sample_hold_H2_K.kicad_sch, part in row 1, column 1]

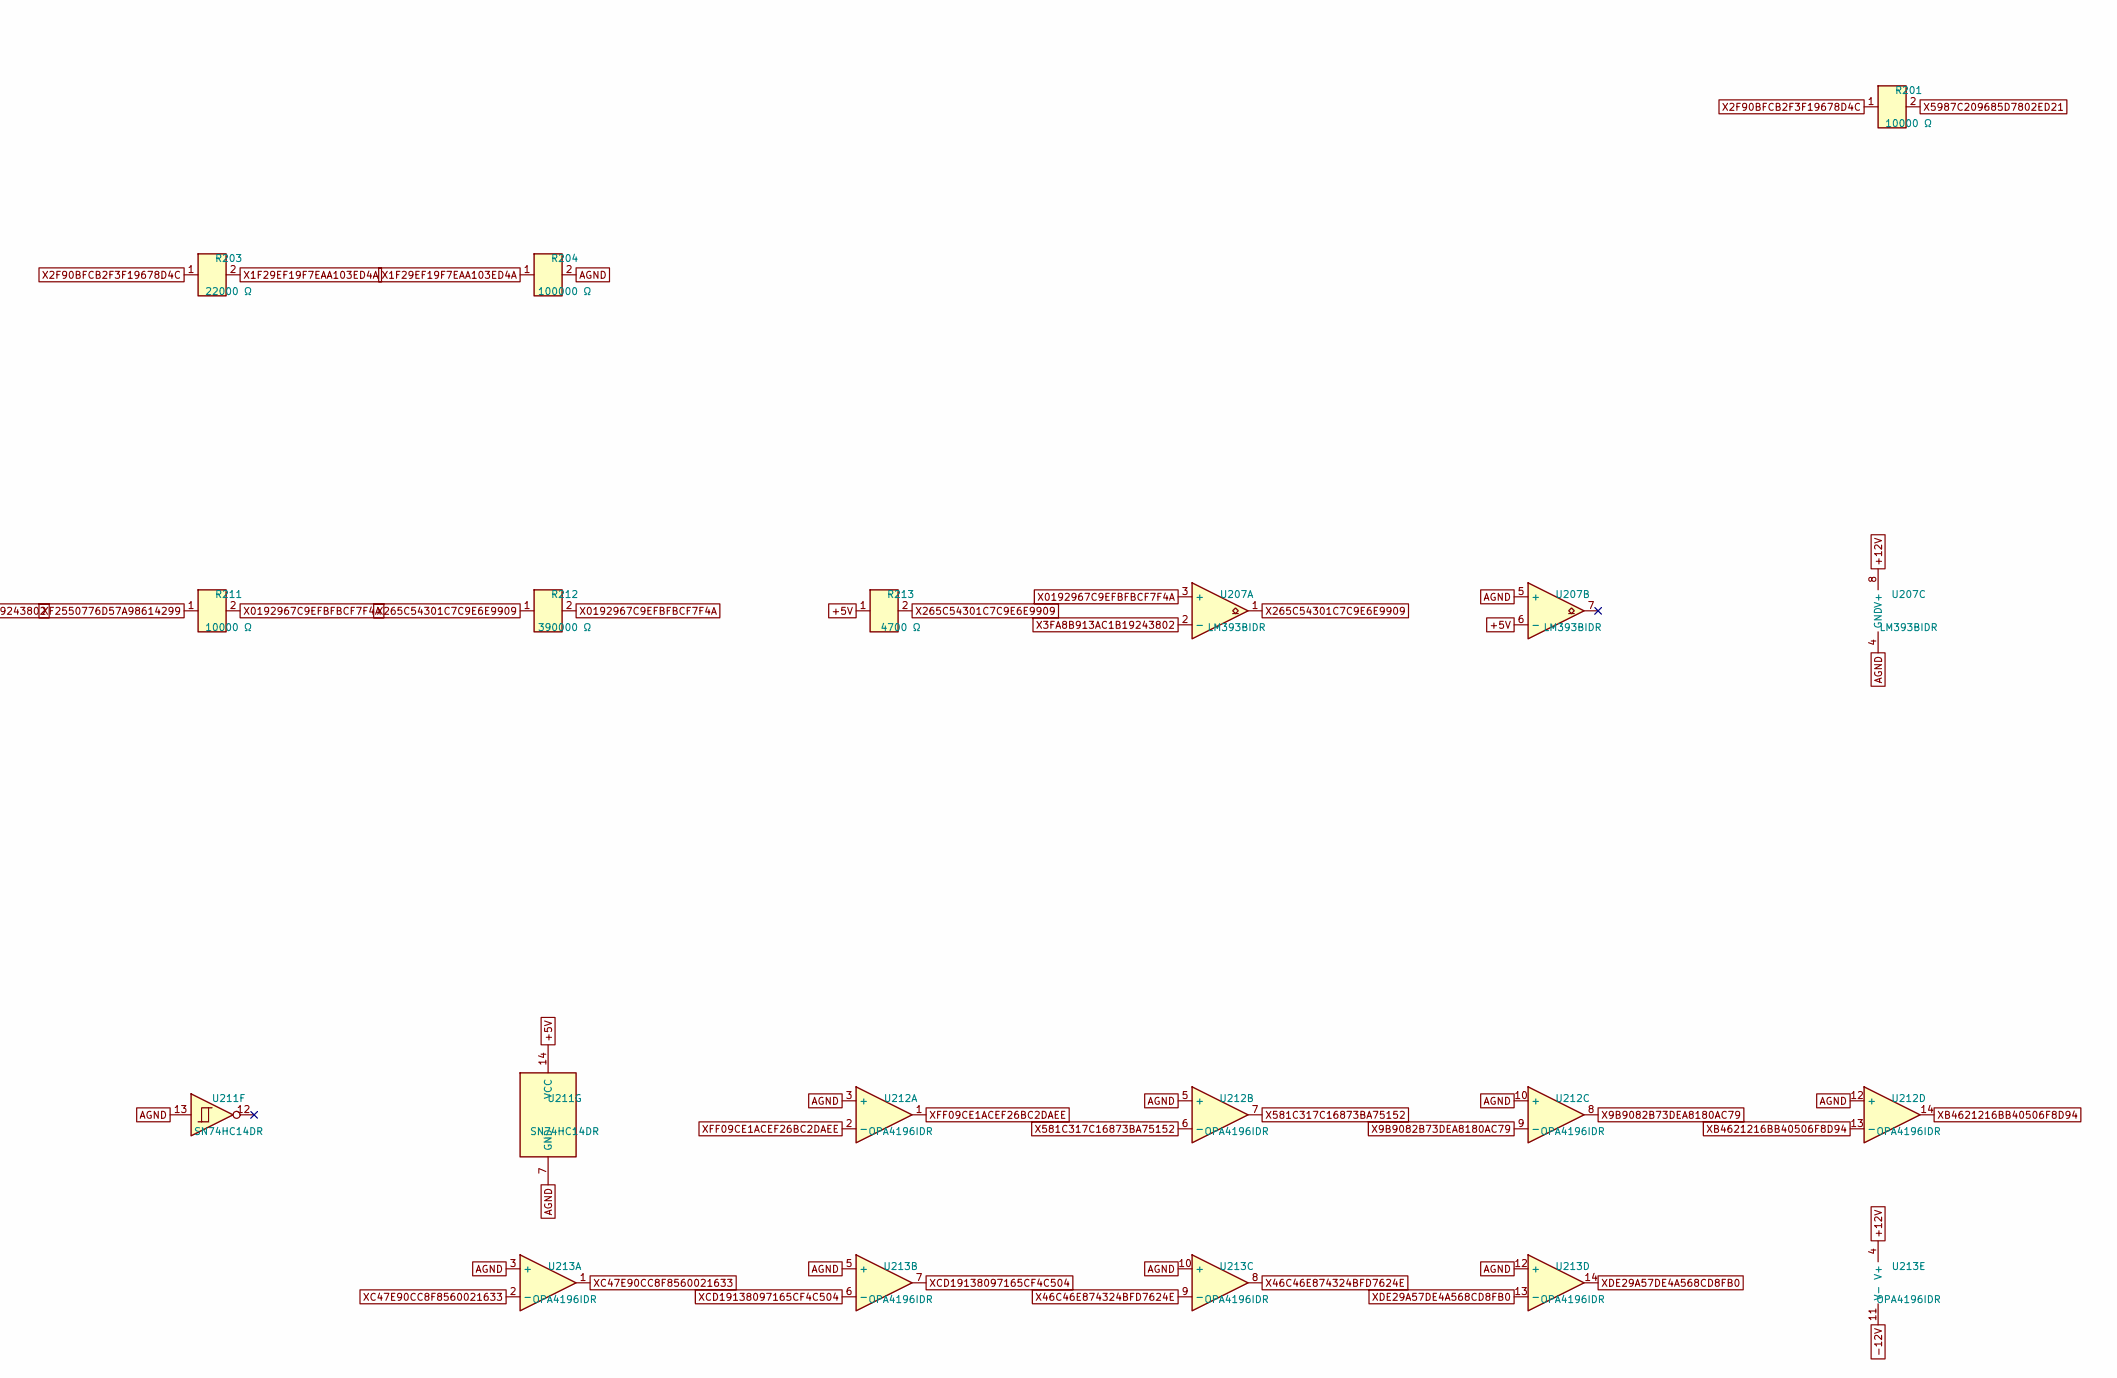
[picture p184: schematic sample_hold_H2_K.kicad_sch, part in row 1, column 2]

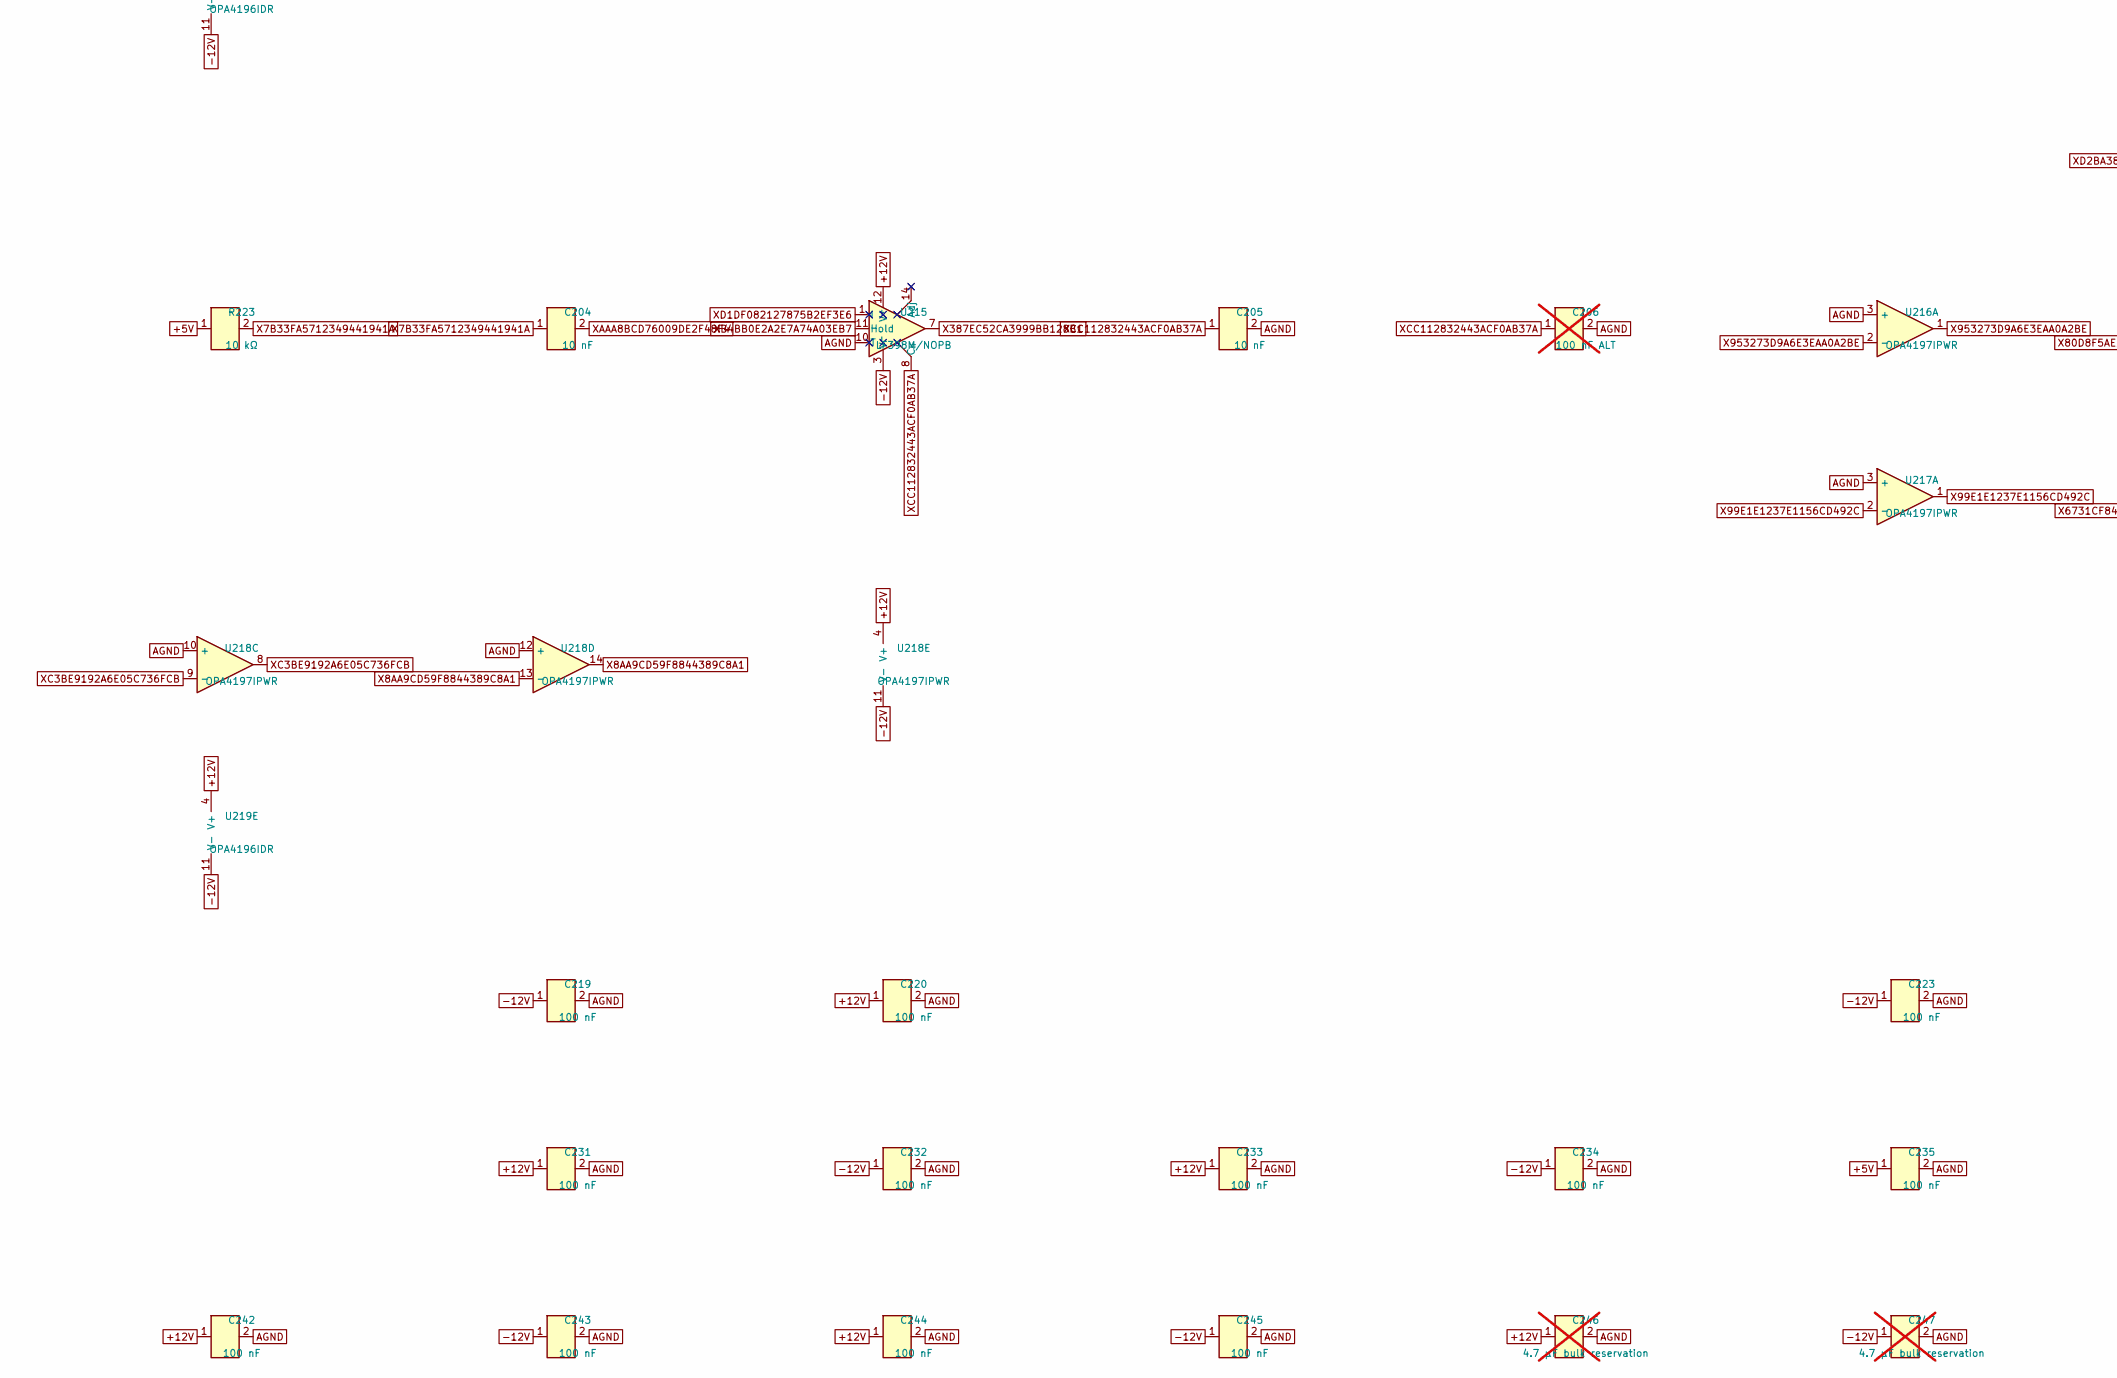
[picture p185: schematic sample_hold_H2_K.kicad_sch, part in row 2, column 1]

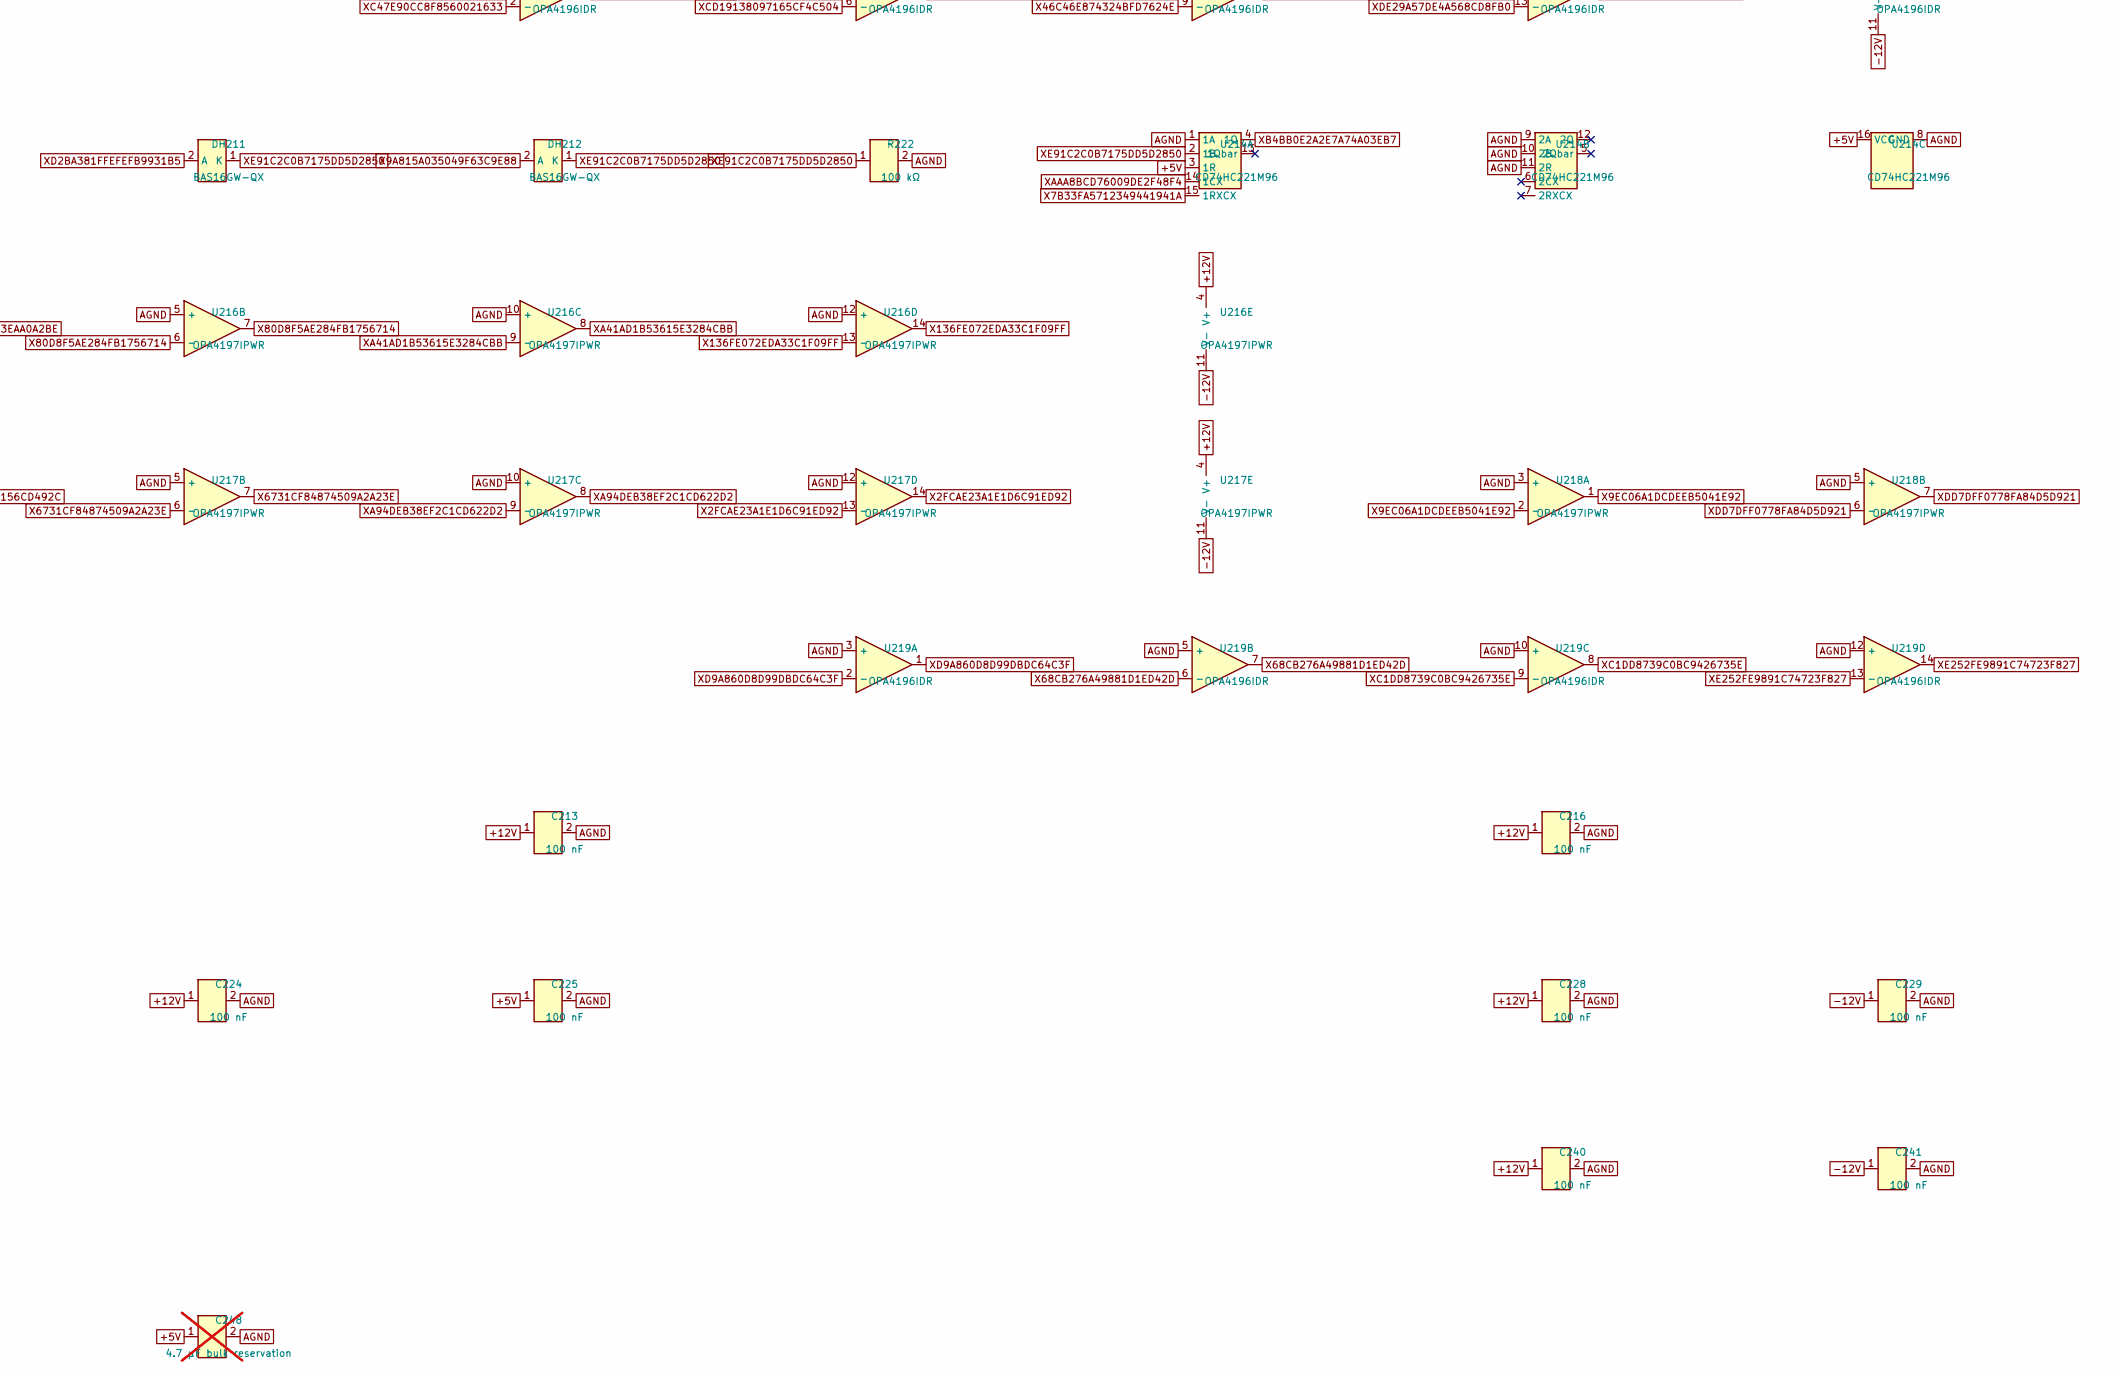
[picture p186: schematic sample_hold_H2_K.kicad_sch, part in row 2, column 2]

Parts:
C201: 1e-07 F; C0603; MPN GRM188R71H104KA93D
C202: 1e-06 F; C0603
C204, C205: 10 nF; C0805; MPN C0805C103J5GACTU; LCSC C2167597
C206: 100 nF ALT; C0805; not fitted
C213, C216, C219, C220, C223, C224, C225, C228, C229, C231, C232, C233, C234, C235, C240, C241, C242, C243, C244, C245: 100 nF; C0603; MPN GRM188R71H104KA93D
C246, C247, C248: 4.7 µF bulk reservation; C0805; MPN GRM21BR61E475KA12L; not fitted
DH211, DH212: BAS16GW-QX; SOD-123; MPN BAS16GW-QX
R201, R202, R211: 10000 Ω; R0603
R203: 22000 Ω; R0603
R204, R209: 100000 Ω; R0603; MPN RT0603BRD07100KL
R210: 33200 Ω; R0603
R212: 390000 Ω; R0603
R213: 4700 Ω; R0603
R222: 100 kΩ; R0603; MPN RC0603FR-07100KL
R223: 10 kΩ; R0603
U201: REF5050AIDR; SOIC-8_3.9x4.9mm_P1.27mm; MPN REF5050AIDR; LCSC C27804
U203, U216, U217, U218: OPA4197IPWR; TSSOP-14_4.4x5mm_P0.65mm; MPN OPA4197IPWR; LCSC C2057327
U207: LM393BIDR; SOIC-8_3.9x4.9mm_P1.27mm; MPN LM393BIDR
U211: SN74HC14DR; SOIC-14_3.9x8.7mm_P1.27mm; MPN SN74HC14DR
U212, U213, U219: OPA4196IDR; SOIC-14_3.9x8.7mm_P1.27mm; MPN OPA4196IDR; LCSC C2057385
U214: CD74HC221M96; SOIC-16_3.9x9.9mm_P1.27mm; MPN CD74HC221M96; LCSC C133954
U215: LF398M/NOPB; SOIC-14_3.9x8.7mm_P1.27mm; MPN LF398M/NOPB; LCSC C1346172

Connections:
+5V: C225.1, C235.1, C248.1, R213.1, R223.1, U207.6 (-), U211.14 (VCC), U214.3 (1R), U214.16 (VCC)
+12V: C201.1, C213.1, C216.1, C220.1, C224.1, C228.1, C231.1, C233.1, C240.1, C242.1, C244.1, C246.1, U201.2 (Vin), U203.4 (V+), U207.8 (V+), U212.4 (V+), U213.4 (V+), U215.12 (V^{+}), U216.4 (V+), U217.4 (V+), U218.4 (V+), U219.4 (V+)
-12V: C219.1, C223.1, C229.1, C232.1, C234.1, C241.1, C243.1, C245.1, C247.1, U203.11 (V-), U212.11 (V-), U213.11 (V-), U215.3 (V^{-}), U216.11 (V-), U217.11 (V-), U218.11 (V-), U219.11 (V-)
AGND: C201.2, C202.2, C205.2, C206.2, C213.2, C216.2, C219.2, C220.2, C223.2, C224.2, C225.2, C228.2, C229.2, C231.2, C232.2, C233.2, C234.2, C235.2, C240.2, C241.2, C242.2, C243.2, C244.2, C245.2, C246.2, C247.2, C248.2, R204.2, R222.2, U201.4 (GND), U203.5 (+), U203.12 (+), U207.4 (GND), U207.5 (+), U211.3, U211.5, U211.7 (GND), U211.9, U211.11, U211.13, U212.3 (+), U212.5 (+), U212.10 (+), U212.12 (+), U213.3 (+), U213.5 (+), U213.10 (+), U213.12 (+), U214.1 (1A), U214.8 (GND), U214.9 (2A), U214.10 (2B), U214.11 (2R), U215.10 (T), U216.3 (+), U216.5 (+), U216.10 (+), U216.12 (+), U217.3 (+), U217.5 (+), U217.10 (+), U217.12 (+), U218.3 (+), U218.5 (+), U218.10 (+), U218.12 (+), U219.3 (+), U219.5 (+), U219.10 (+), U219.12 (+)
X1F29EF19F7EAA103ED4A: R203.2, R204.1, U203.10 (+)
X2F90BFCB2F3F19678D4C: R201.1, R203.1, R210.1, U203.1, U203.2 (-)
X2FCAE23A1E1D6C91ED92: U217.13 (-), U217.14
X3FA8B913AC1B19243802: R209.2, R210.2, U207.2 (-)
X5E8567ED0948C89AC941: R202.1, U203.7
X7B33FA5712349441941A: C204.1, R223.2, U214.15 (1RXCX)
X8AA9CD59F8844389C8A1: U218.13 (-), U218.14
X8D252F56F988D1134987: U203.13 (-), U203.14
X9A815A035049F63C9E88: DH212.2 (A)
X9B9082B73DEA8180AC79: U212.8, U212.9 (-)
X9EC06A1DCDEEB5041E92: U218.1, U218.2 (-)
X46C46E874324BFD7624E: U213.8, U213.9 (-)
X68CB276A49881D1ED42D: U219.6 (-), U219.7
X80D8F5AE284FB1756714: U216.6 (-), U216.7
X99E1E1237E1156CD492C: U217.1, U217.2 (-)
X136FE072EDA33C1F09FF: U216.13 (-), U216.14
X265C54301C7C9E6E9909: R212.1, R213.2, U207.1, U211.1
X387EC52CA3999BB128B1: U215.7
X581C317C16873BA75152: U212.6 (-), U212.7
X5987C209685D7802ED21: R201.2, R202.2, U203.6 (-)
X6731CF84874509A2A23E: U217.6 (-), U217.7
X0192967C9EFBFBCF7F4A: R211.2, R212.2, U207.3 (+)
X953273D9A6E3EAA0A2BE: U216.1, U216.2 (-)
XA41AD1B53615E3284CBB: U216.8, U216.9 (-)
XA94DEB38EF2C1CD622D2: U217.8, U217.9 (-)
XAAA8BCD76009DE2F48F4: C204.2, U214.14 (1CX)
XB4BB0E2A2E7A74A03EB7: U214.4 (1Q), U215.11 (Hold)
XB4621216BB40506F8D94: U212.13 (-), U212.14
XC1DD8739C0BC9426735E: U219.8, U219.9 (-)
XC3BE9192A6E05C736FCB: U218.8, U218.9 (-)
XC8DFE86BD3A7EAD286C6: R209.1
XC47E90CC8F8560021633: U213.1, U213.2 (-)
XCC112832443ACF0AB37A: C205.1, C206.1, U215.8 (C_{h})
XCD19138097165CF4C504: U213.6 (-), U213.7
XD1DF082127875B2EF3E6: U215.1 (I)
XD2BA381FFEFEFB9931B5: DH211.2 (A), U211.2
XD9A860D8D99DBDC64C3F: U219.1, U219.2 (-)
XDD7DFF0778FA84D5D921: U218.6 (-), U218.7
XDE29A57DE4A568CD8FB0: U213.13 (-), U213.14
XE4AD3562BFC313941633: C202.1, U201.6 (Vout), U203.3 (+)
XE91C2C0B7175DD5D2850: DH211.1 (K), DH212.1 (K), R222.1, U214.2 (1B)
XE252FE9891C74723F827: U219.13 (-), U219.14
XF2550776D57A98614299: R211.1, U203.8, U203.9 (-)
XFF09CE1ACEF26BC2DAEE: U212.1, U212.2 (-)
