Takazudo/zudo-osc-hole-field/boards/osc-core/sheets/wavefolder_W1_K.kicad_sch

## KiCad design boards/osc-core/sheets/wavefolder_W1_K.kicad_sch (2026-10-05)

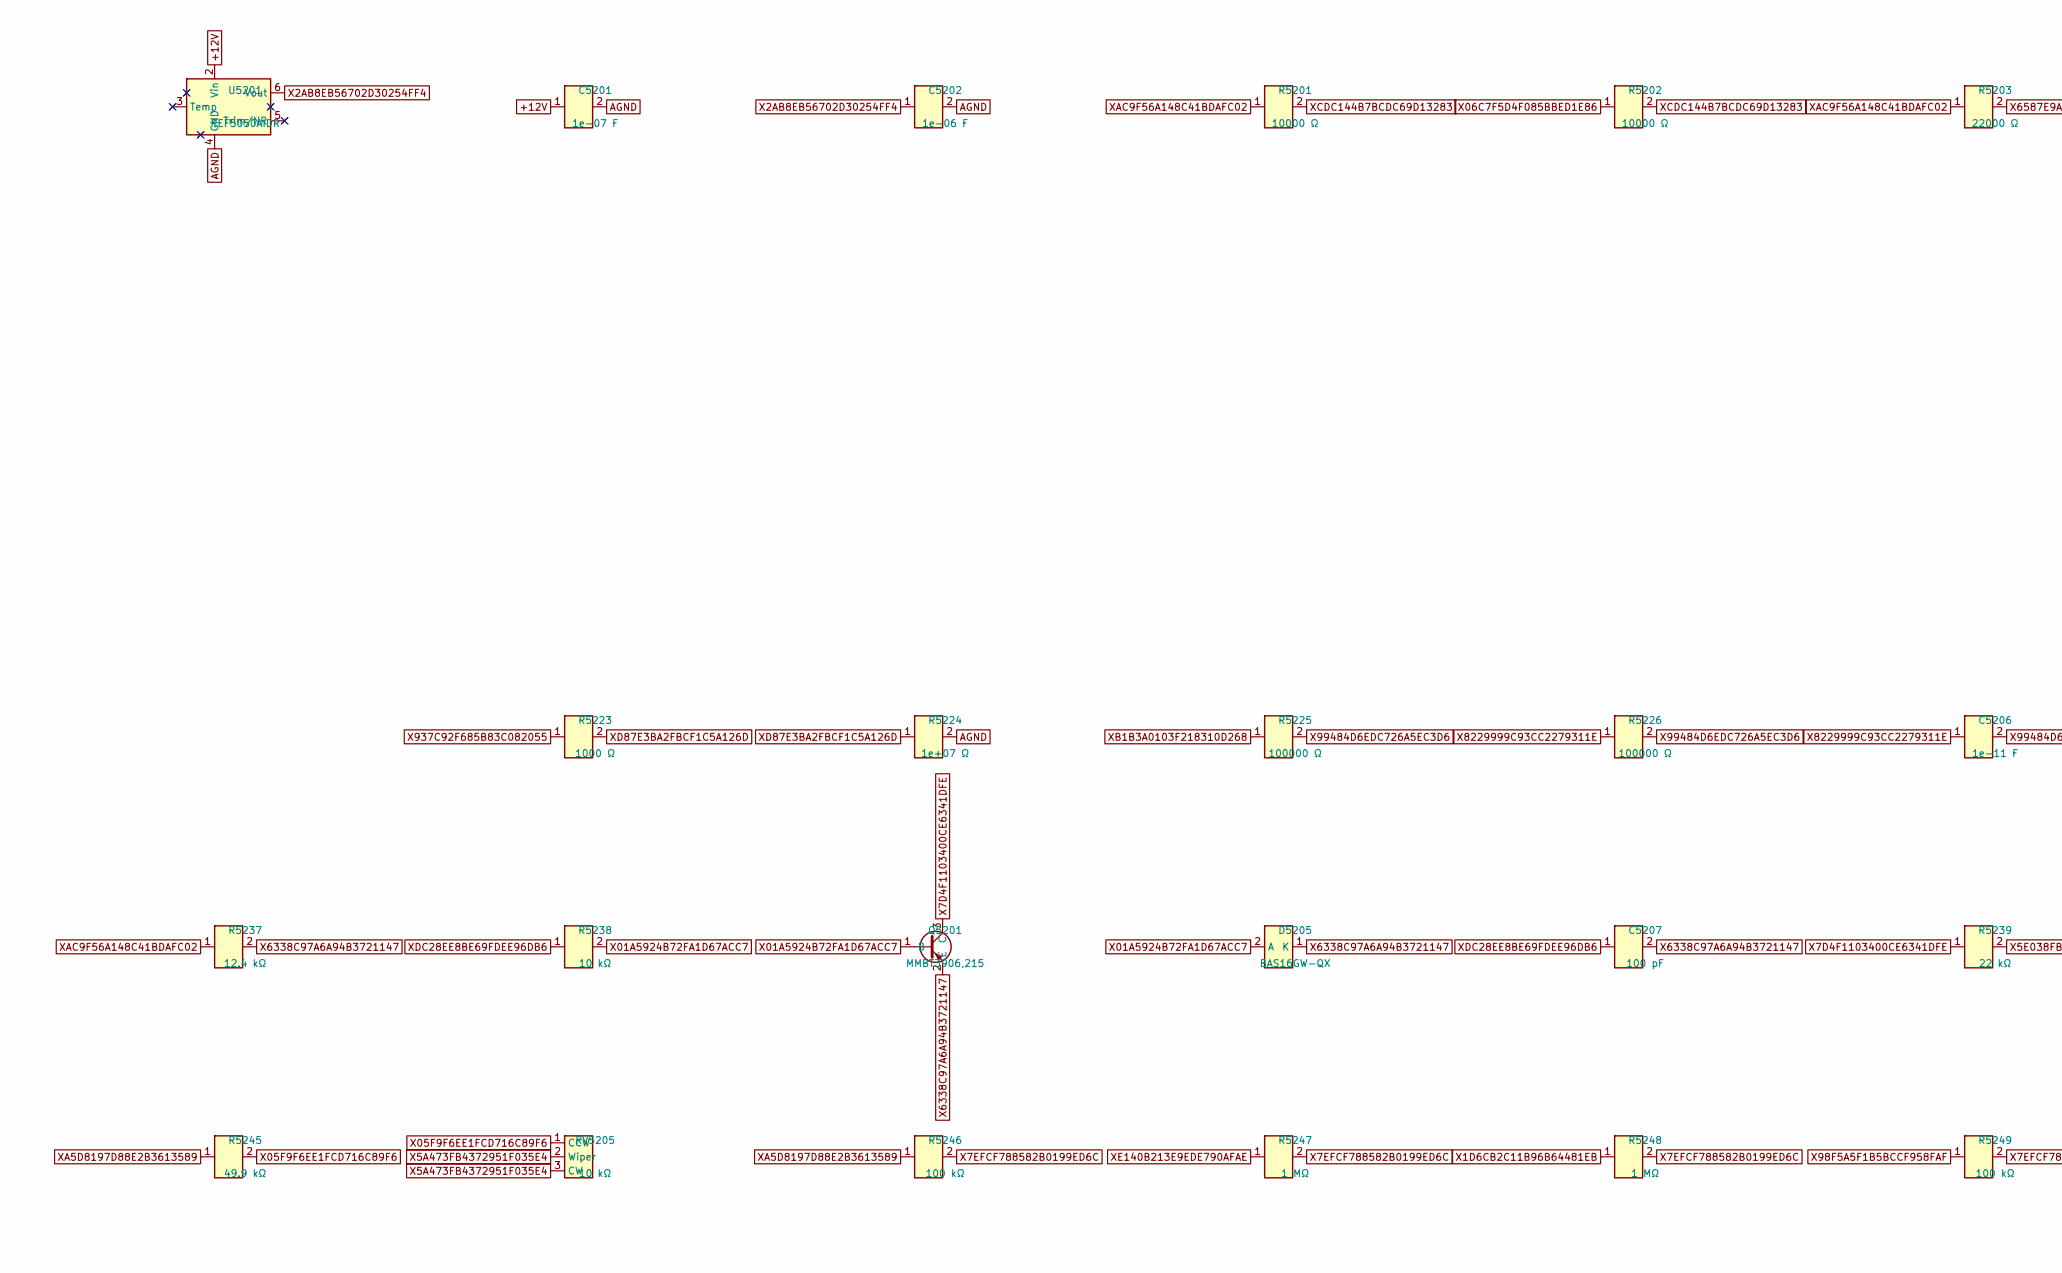
[picture p187: schematic wavefolder_W1_K.kicad_sch, part in row 1, column 1]

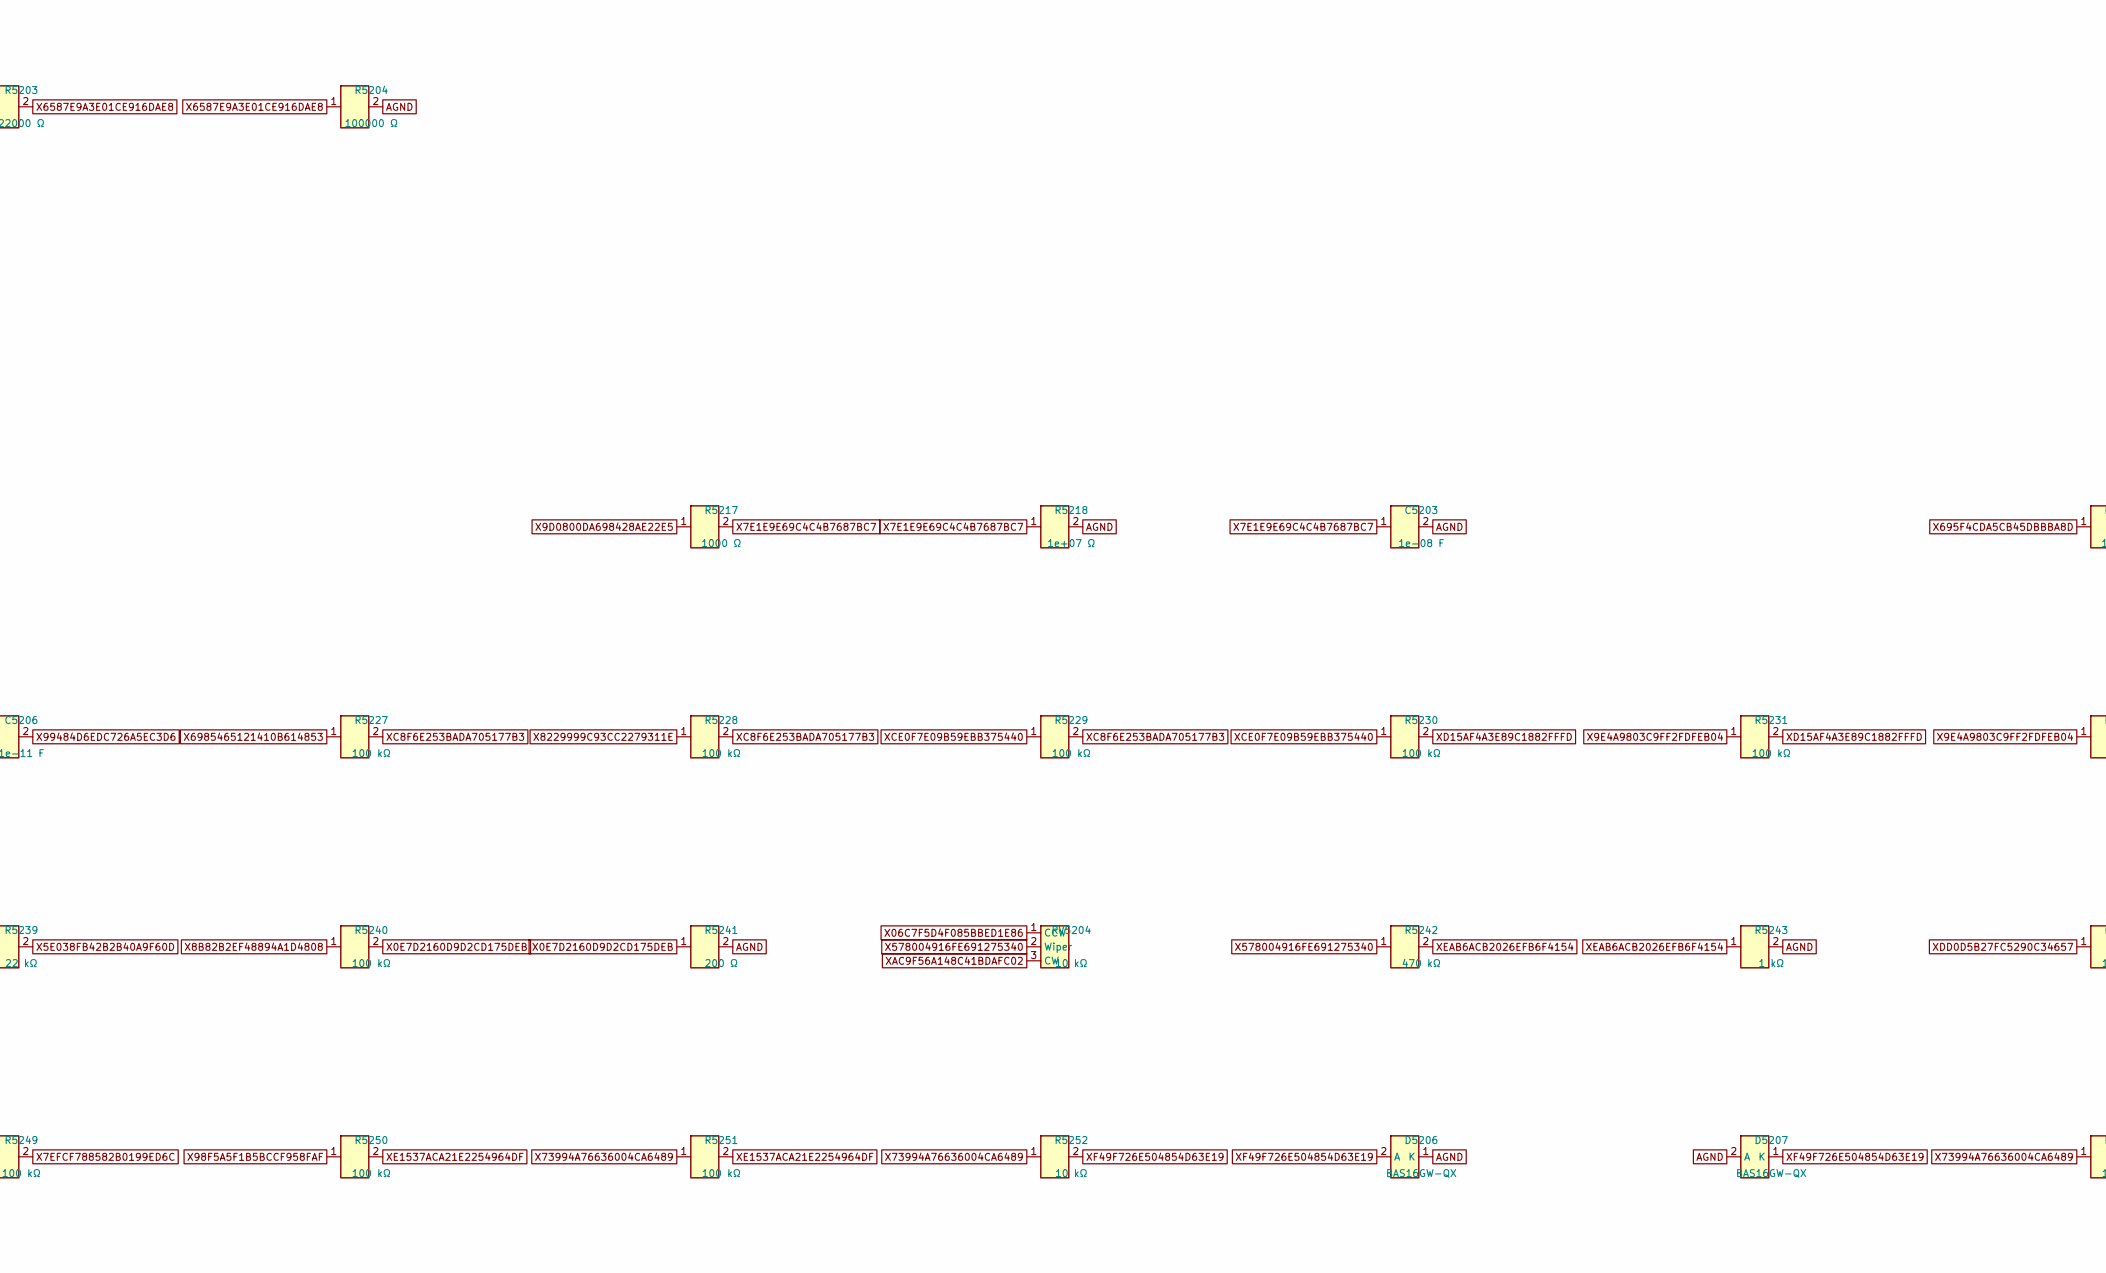
[picture p188: schematic wavefolder_W1_K.kicad_sch, part in row 1, column 2]

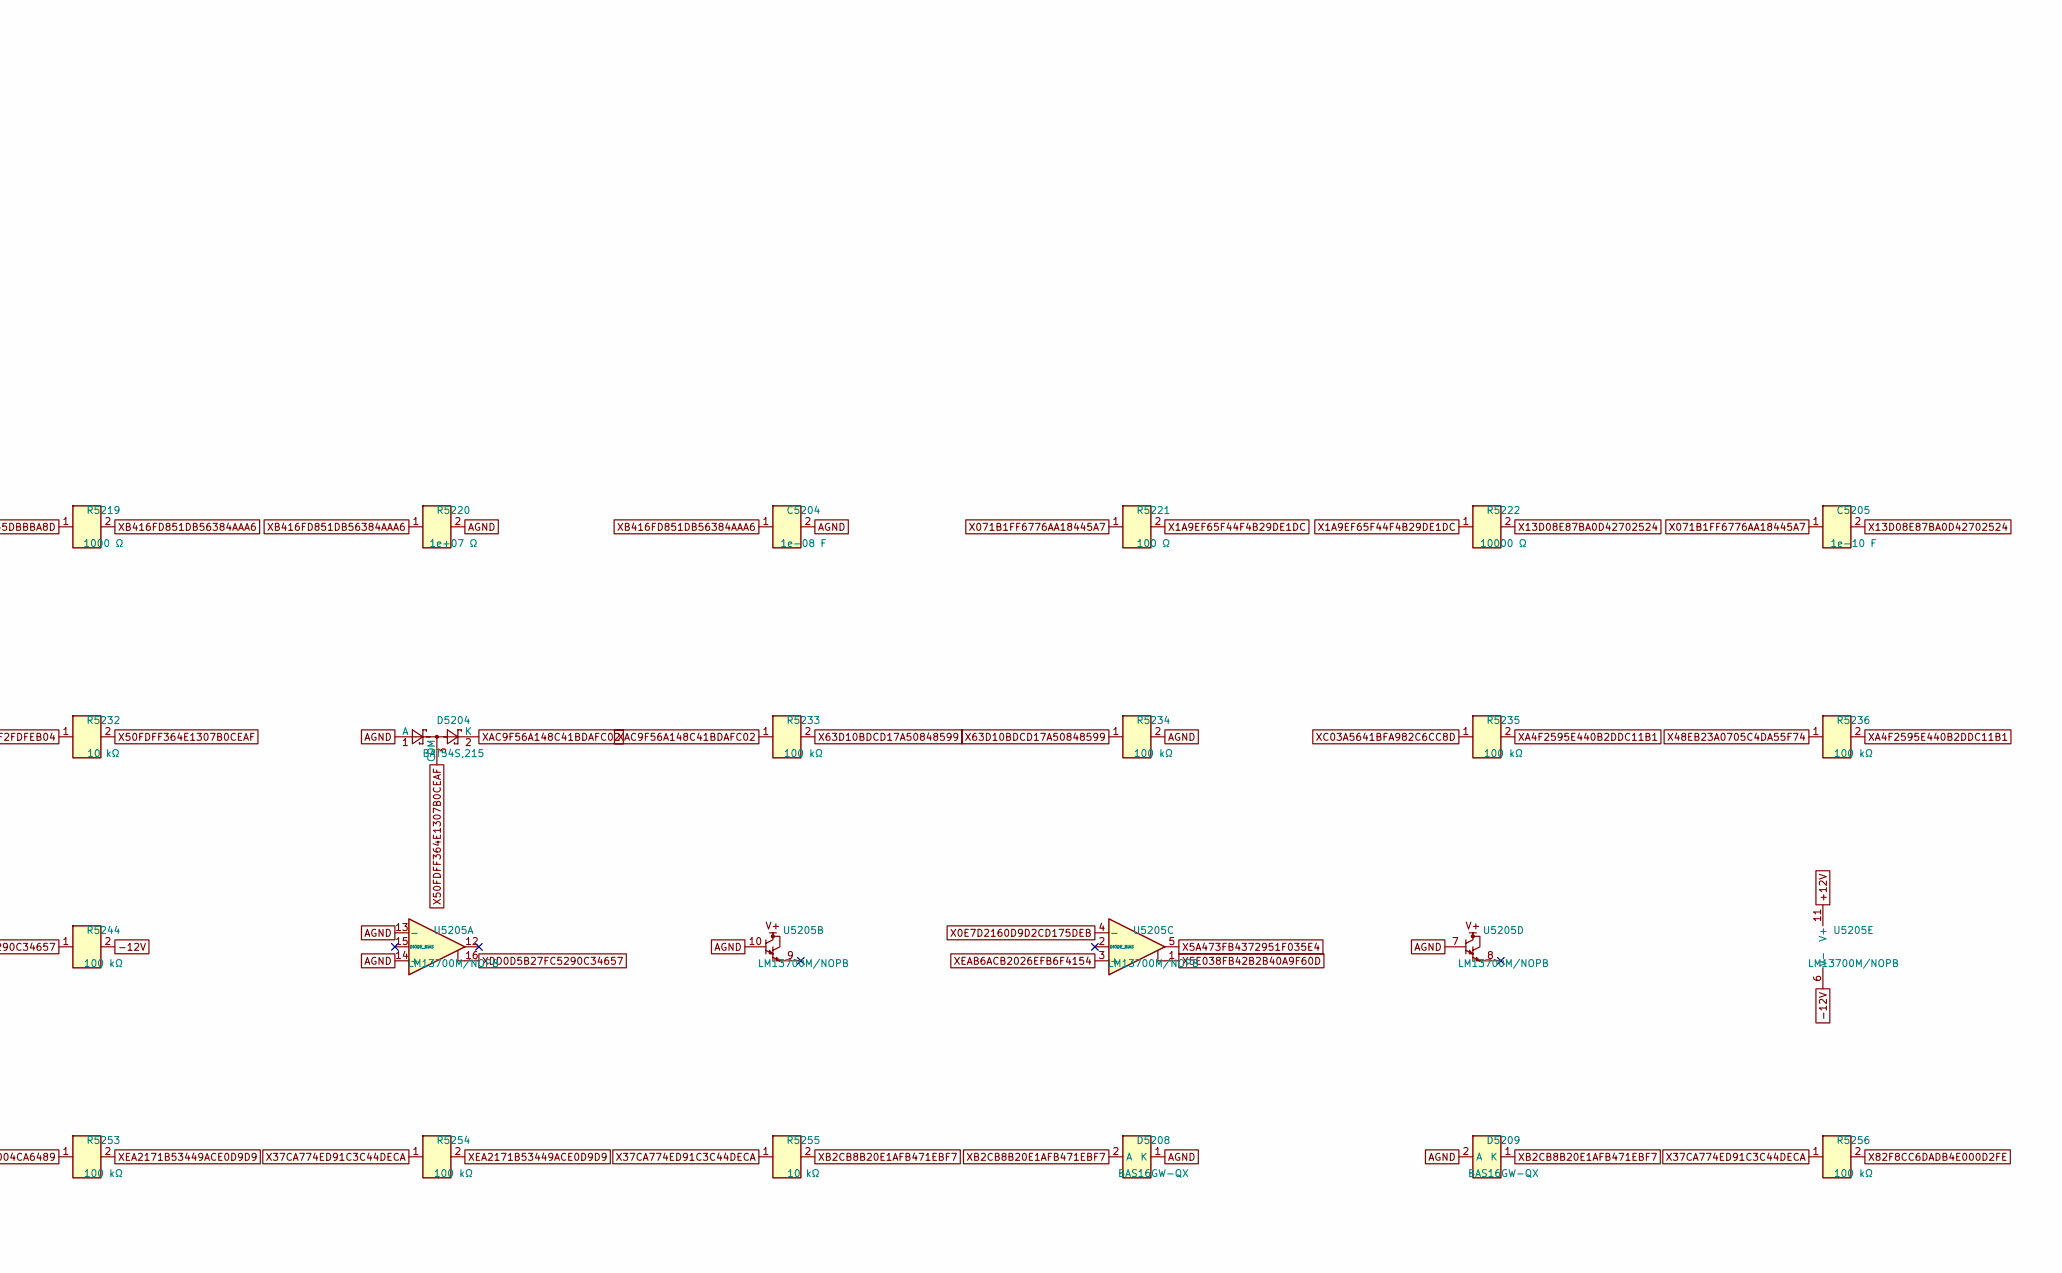
[picture p189: schematic wavefolder_W1_K.kicad_sch, part in row 1, column 3]

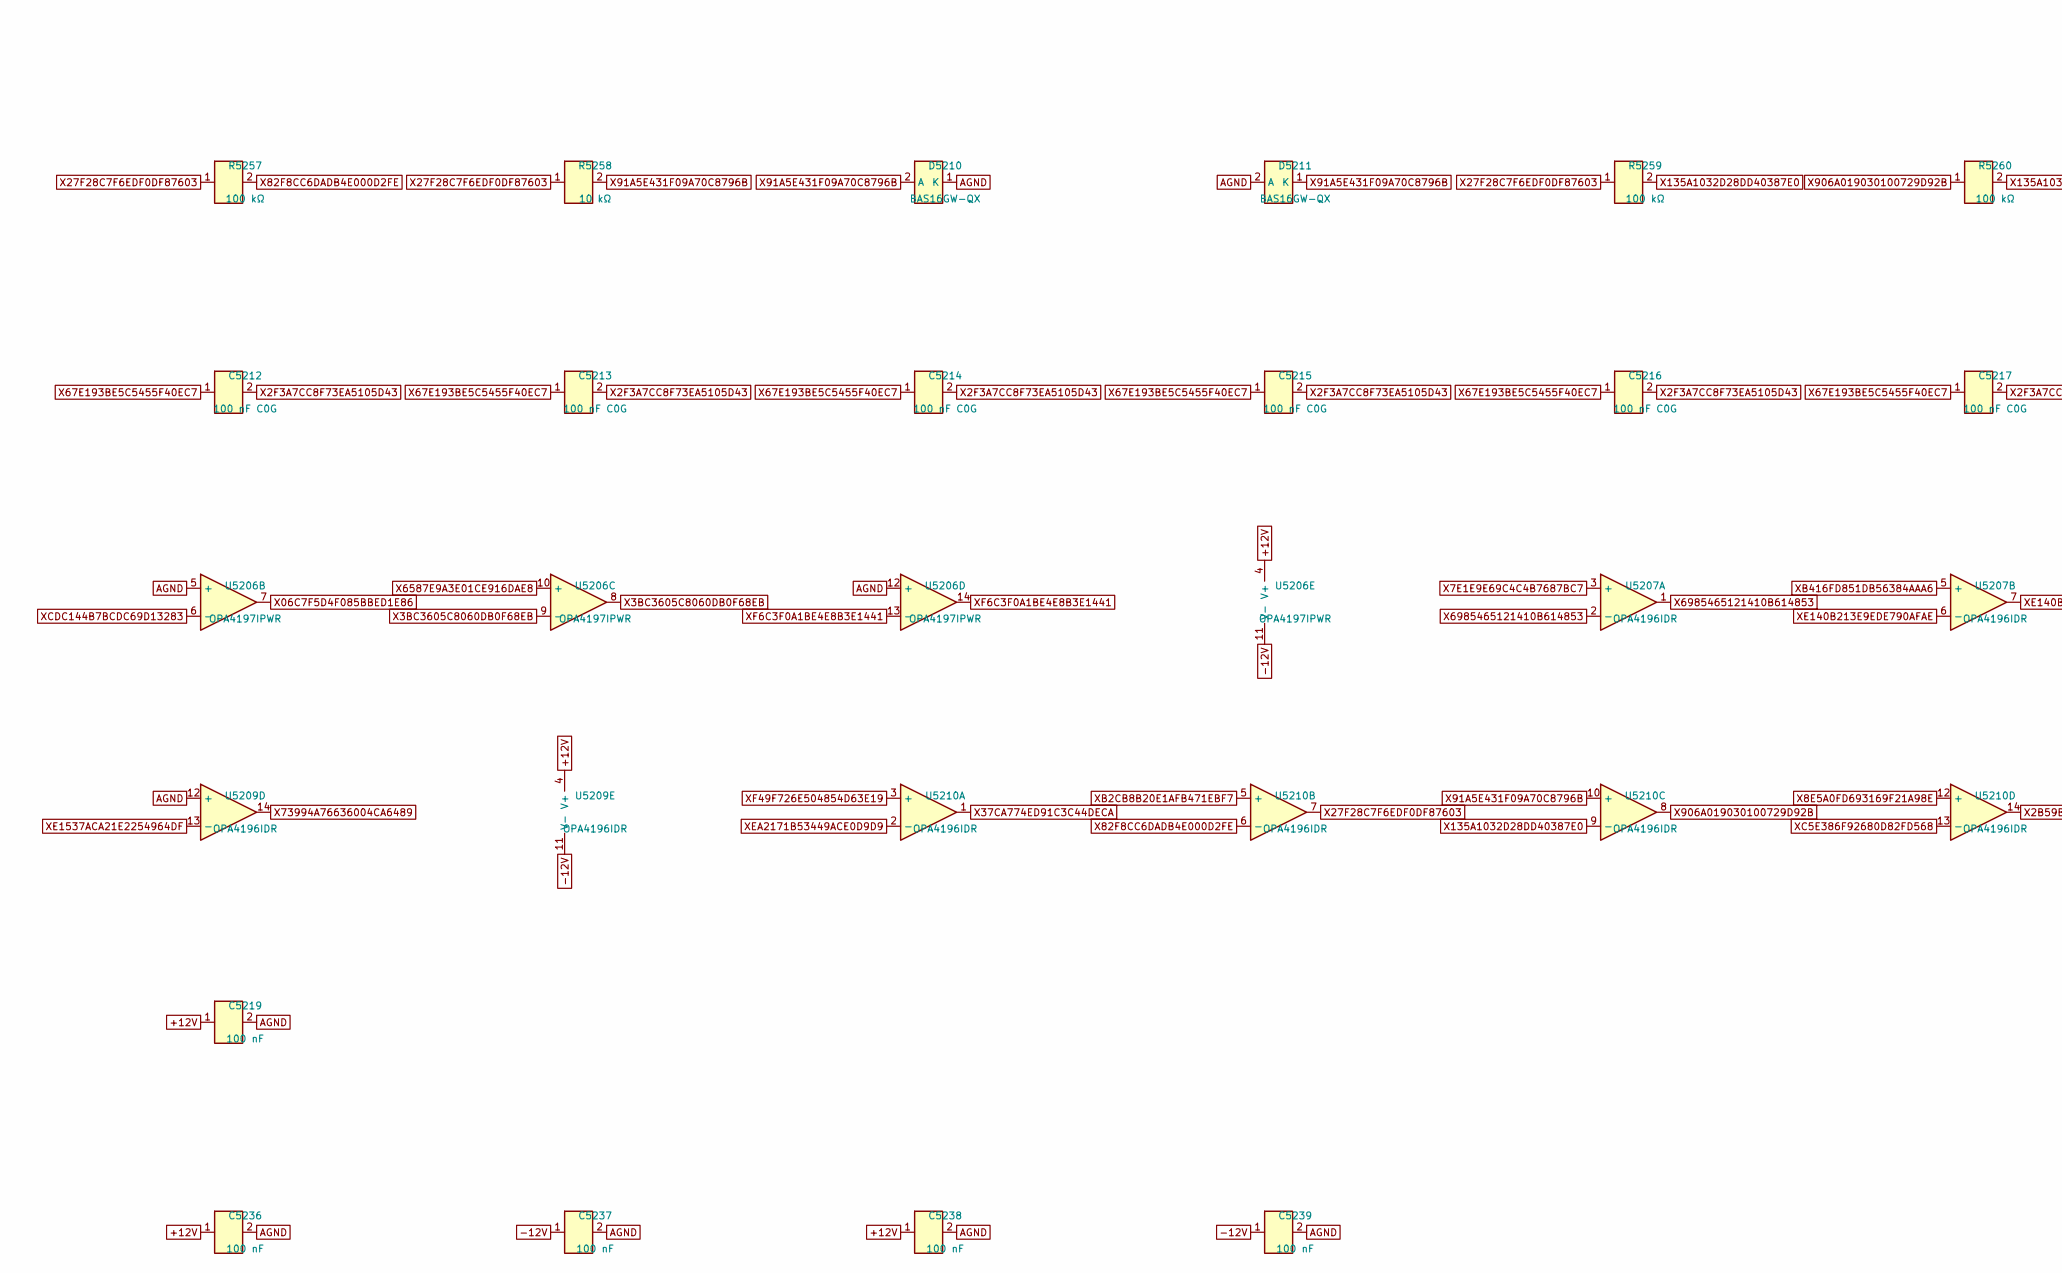
[picture p190: schematic wavefolder_W1_K.kicad_sch, part in row 2, column 1]

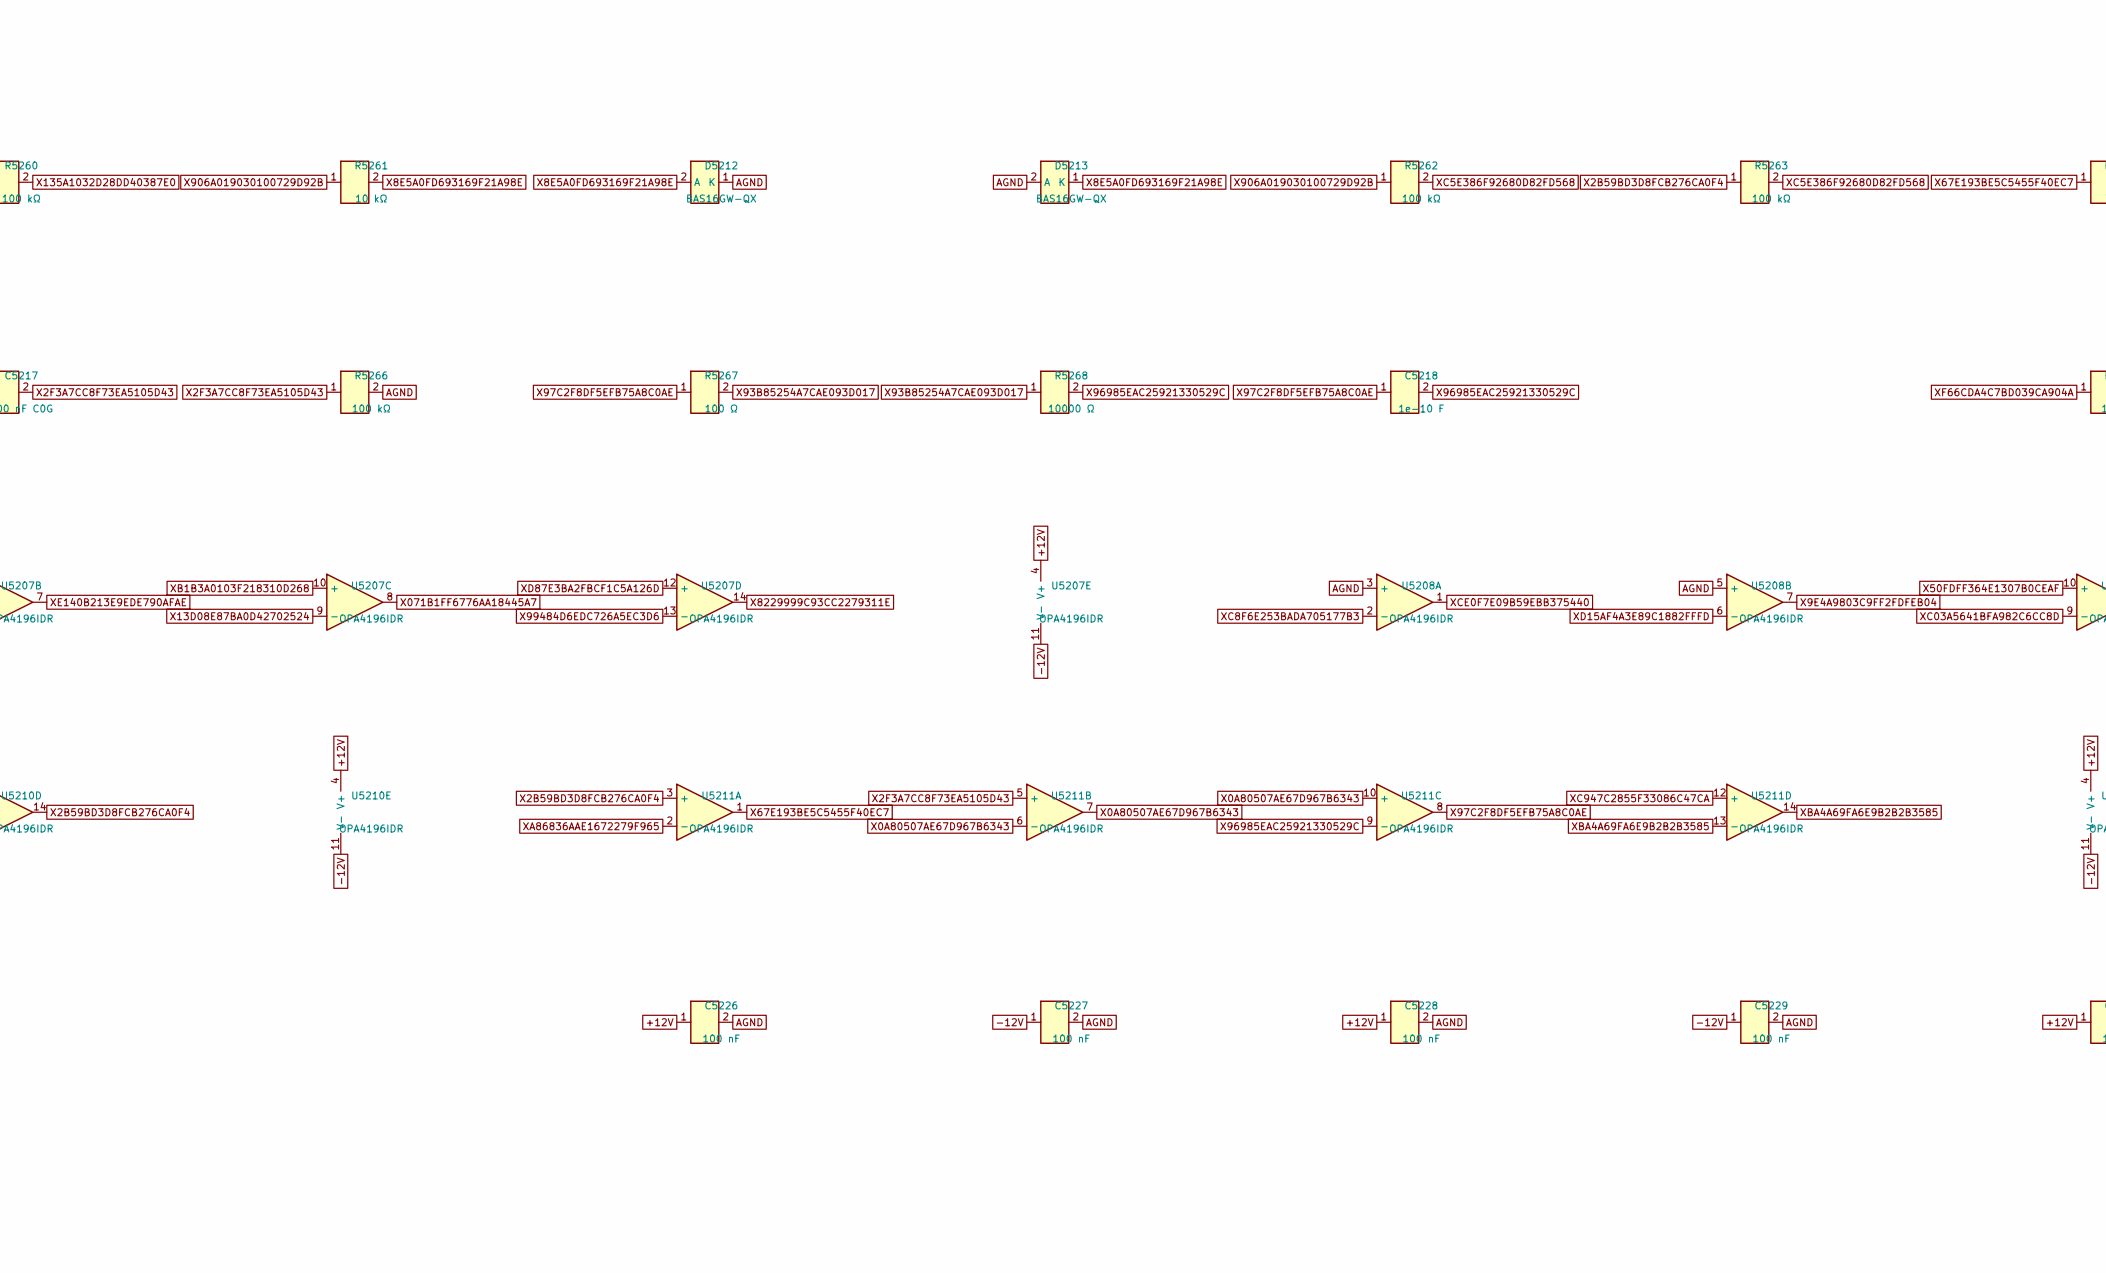
[picture p191: schematic wavefolder_W1_K.kicad_sch, part in row 2, column 2]

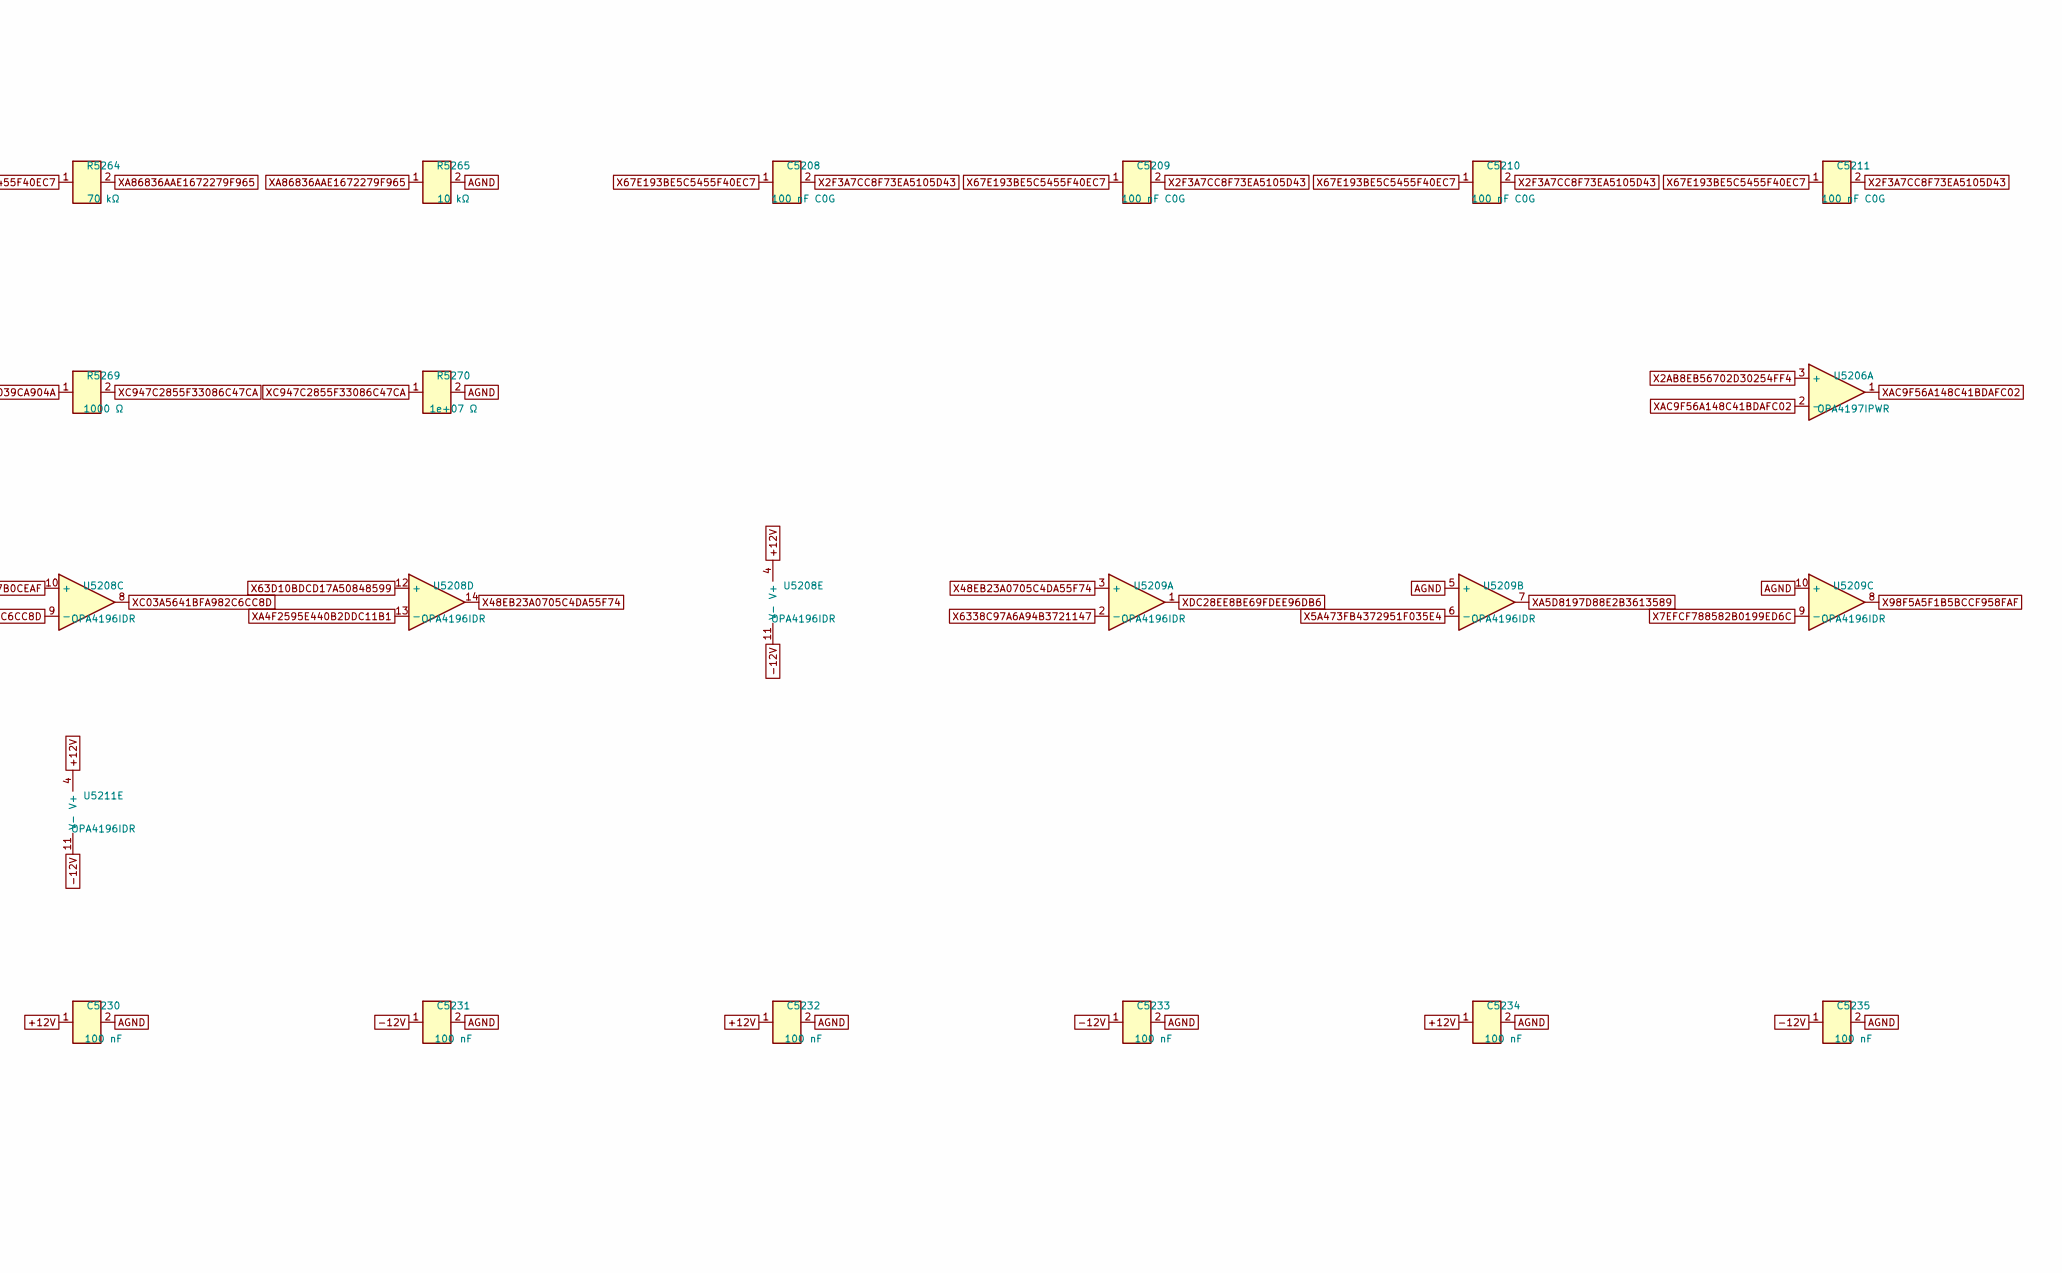
[picture p192: schematic wavefolder_W1_K.kicad_sch, part in row 2, column 3]

Parts:
C5201: 1e-07 F; C0603; MPN GRM188R71H104KA93D
C5202: 1e-06 F; C0603
C5203, C5204: 1e-08 F; C0603
C5205, C5218: 1e-10 F; C0603; MPN C0603C101J5GACTU
C5206: 1e-11 F; C0603
C5207: 100 pF; C0603; MPN C0603C101J5GACTU
C5208, C5209, C5210, C5211, C5212, C5213, C5214, C5215, C5216, C5217: 100 nF C0G; C1206; MPN 1206CG104J500NT; LCSC C46348
C5219, C5226, C5227, C5228, C5229, C5230, C5231, C5232, C5233, C5234, C5235, C5236, C5237, C5238, C5239: 100 nF; C0603; MPN GRM188R71H104KA93D
D5204: BAT54S,215; SOT-23; MPN BAT54S,215
D5205, D5206, D5207, D5208, D5209, D5210, D5211, D5212, D5213: BAS16GW-QX; SOD-123; MPN BAS16GW-QX
Q5201: MMBT3906,215; SOT-23; MPN MMBT3906,215
R5201, R5202, R5222, R5268: 10000 Ω; R0603
R5203: 22000 Ω; R0603
R5204, R5225, R5226: 100000 Ω; R0603; MPN RT0603BRD07100KL
R5217, R5219, R5223, R5269: 1000 Ω; R0603
R5218, R5220, R5224, R5270: 1e+07 Ω; R0603
R5221, R5267: 100 Ω; R0603
R5227, R5228, R5229, R5230, R5231, R5233, R5234, R5235, R5236, R5240, R5244, R5246, R5249, R5250, R5251, R5253, R5254, R5256, R5257, R5259, R5260, R5262, R5263, R5266: 100 kΩ; R0603; MPN RT0603BRD07100KL
R5232, R5238, R5252, R5255, R5258, R5261, R5265: 10 kΩ; R0603
R5237: 12.4 kΩ; R0603
R5239: 22 kΩ; R0603
R5241: 200 Ω; R0603
R5242: 470 kΩ; R0603
R5243: 1 kΩ; R0603
R5245: 49.9 kΩ; R0603
R5247, R5248: 1 MΩ; R0603
R5264: 70 kΩ; R0603
RV5204, RV5205: 10 kΩ; Potentiometer_Bourns_TC33X_Vertical; MPN TC33X-2-103E
U5201: REF5050AIDR; SOIC-8_3.9x4.9mm_P1.27mm; MPN REF5050AIDR; LCSC C27804
U5205: LM13700M/NOPB; SOIC-16_3.9x9.9mm_P1.27mm; MPN LM13700M/NOPB; LCSC C1346265
U5206: OPA4197IPWR; TSSOP-14_4.4x5mm_P0.65mm; MPN OPA4197IPWR; LCSC C2057327
U5207, U5208, U5209, U5210, U5211: OPA4196IDR; SOIC-14_3.9x8.7mm_P1.27mm; MPN OPA4196IDR; LCSC C2057385

Connections:
+12V: C5201.1, C5219.1, C5226.1, C5228.1, C5230.1, C5232.1, C5234.1, C5236.1, C5238.1, U5201.2 (Vin), U5205.11 (V+), U5206.4 (V+), U5207.4 (V+), U5208.4 (V+), U5209.4 (V+), U5210.4 (V+), U5211.4 (V+)
-12V: C5227.1, C5229.1, C5231.1, C5233.1, C5235.1, C5237.1, C5239.1, R5244.2, U5205.6 (V-), U5206.11 (V-), U5207.11 (V-), U5208.11 (V-), U5209.11 (V-), U5210.11 (V-), U5211.11 (V-)
AGND: C5201.2, C5202.2, C5203.2, C5204.2, C5219.2, C5226.2, C5227.2, C5228.2, C5229.2, C5230.2, C5231.2, C5232.2, C5233.2, C5234.2, C5235.2, C5236.2, C5237.2, C5238.2, C5239.2, D5204.1 (A), D5206.1 (K), D5207.2 (A), D5208.1 (K), D5209.2 (A), D5210.1 (K), D5211.2 (A), D5212.1 (K), D5213.2 (A), R5204.2, R5218.2, R5220.2, R5224.2, R5234.2, R5241.2, R5243.2, R5265.2, R5266.2, R5270.2, U5201.4 (GND), U5205.7, U5205.10, U5205.13 (-), U5205.14 (+), U5206.5 (+), U5206.12 (+), U5208.3 (+), U5208.5 (+), U5209.5 (+), U5209.10 (+), U5209.12 (+)
X0A80507AE67D967B6343: U5211.6 (-), U5211.7, U5211.10 (+)
X0E7D2160D9D2CD175DEB: R5240.2, R5241.1, U5205.4 (-)
X1A9EF65F44F4B29DE1DC: R5221.2, R5222.1
X01A5924B72FA1D67ACC7: D5205.2 (A), Q5201.1 (B), R5238.2
X1D6CB2C11B96B64481EB: R5248.1
X2AB8EB56702D30254FF4: C5202.1, U5201.6 (Vout), U5206.3 (+)
X2B59BD3D8FCB276CA0F4: R5263.1, U5210.14, U5211.3 (+)
X2F3A7CC8F73EA5105D43: C5208.2, C5209.2, C5210.2, C5211.2, C5212.2, C5213.2, C5214.2, C5215.2, C5216.2, C5217.2, R5266.1, U5211.5 (+)
X3BC3605C8060DB0F68EB: U5206.8, U5206.9 (-)
X5A473FB4372951F035E4: RV5205.2 (Wiper), RV5205.3 (CW), U5205.5, U5209.6 (-)
X5E038FB42B2B40A9F60D: R5239.2, U5205.1
X05F9F6EE1FCD716C89F6: R5245.2, RV5205.1 (CCW)
X06C7F5D4F085BBED1E86: R5202.1, RV5204.1 (CCW), U5206.7
X7D4F1103400CE6341DFE: Q5201.3 (C), R5239.1
X7E1E9E69C4C4B7687BC7: C5203.1, R5217.2, R5218.1, U5207.3 (+)
X7EFCF788582B0199ED6C: R5246.2, R5247.2, R5248.2, R5249.2, U5209.9 (-)
X8B82B2EF48894A1D4808: R5240.1
X8E5A0FD693169F21A98E: D5212.2 (A), D5213.1 (K), R5261.2, U5210.12 (+)
X9D0800DA698428AE22E5: R5217.1
X9E4A9803C9FF2FDFEB04: R5231.1, R5232.1, U5208.7
X13D08E87BA0D42702524: C5205.2, R5222.2, U5207.9 (-)
X27F28C7F6EDF0DF87603: R5257.1, R5258.1, R5259.1, U5210.7
X37CA774ED91C3C44DECA: R5254.1, R5255.1, R5256.1, U5210.1
X48EB23A0705C4DA55F74: R5236.1, U5208.14, U5209.3 (+)
X50FDFF364E1307B0CEAF: D5204.3 (COM), R5232.2, U5208.10 (+)
X63D10BDCD17A50848599: R5233.2, R5234.1, U5208.12 (+)
X67E193BE5C5455F40EC7: C5208.1, C5209.1, C5210.1, C5211.1, C5212.1, C5213.1, C5214.1, C5215.1, C5216.1, C5217.1, R5264.1, U5211.1
X071B1FF6776AA18445A7: C5205.1, R5221.1, U5207.8
X82F8CC6DADB4E000D2FE: R5256.2, R5257.2, U5210.6 (-)
X91A5E431F09A70C8796B: D5210.2 (A), D5211.1 (K), R5258.2, U5210.10 (+)
X93B85254A7CAE093D017: R5267.2, R5268.1
X97C2F8DF5EFB75A8C0AE: C5218.1, R5267.1, U5211.8
X98F5A5F1B5BCCF958FAF: R5249.1, R5250.1, U5209.8
X135A1032D28DD40387E0: R5259.2, R5260.2, U5210.9 (-)
X695F4CDA5CB45DBBBA8D: R5219.1
X906A019030100729D92B: R5260.1, R5261.1, R5262.1, U5210.8
X937C92F685B83C082055: R5223.1
X6338C97A6A94B3721147: C5207.2, D5205.1 (K), Q5201.2 (E), R5237.2, U5209.2 (-)
X6587E9A3E01CE916DAE8: R5203.2, R5204.1, U5206.10 (+)
X73994A76636004CA6489: R5251.1, R5252.1, R5253.1, U5209.14
X96985EAC25921330529C: C5218.2, R5268.2, U5211.9 (-)
X99484D6EDC726A5EC3D6: C5206.2, R5225.2, R5226.2, U5207.13 (-)
X8229999C93CC2279311E: C5206.1, R5226.1, R5228.1, U5207.14
X578004916FE691275340: R5242.1, RV5204.2 (Wiper)
X6985465121410B614853: R5227.1, U5207.1, U5207.2 (-)
XA4F2595E440B2DDC11B1: R5235.2, R5236.2, U5208.13 (-)
XA5D8197D88E2B3613589: R5245.1, R5246.1, U5209.7
XA86836AAE1672279F965: R5264.2, R5265.1, U5211.2 (-)
XAC9F56A148C41BDAFC02: D5204.2 (K), R5201.1, R5203.1, R5233.1, R5237.1, RV5204.3 (CW), U5206.1, U5206.2 (-)
XB1B3A0103F218310D268: R5225.1, U5207.10 (+)
XB2CB8B20E1AFB471EBF7: D5208.2 (A), D5209.1 (K), R5255.2, U5210.5 (+)
XB416FD851DB56384AAA6: C5204.1, R5219.2, R5220.1, U5207.5 (+)
XBA4A69FA6E9B2B2B3585: U5211.13 (-), U5211.14
XC03A5641BFA982C6CC8D: R5235.1, U5208.8, U5208.9 (-)
XC5E386F92680D82FD568: R5262.2, R5263.2, U5210.13 (-)
XC8F6E253BADA705177B3: R5227.2, R5228.2, R5229.2, U5208.2 (-)
XC947C2855F33086C47CA: R5269.2, R5270.1, U5211.12 (+)
XCDC144B7BCDC69D13283: R5201.2, R5202.2, U5206.6 (-)
XCE0F7E09B59EBB375440: R5229.1, R5230.1, U5208.1
XD15AF4A3E89C1882FFFD: R5230.2, R5231.2, U5208.6 (-)
XD87E3BA2FBCF1C5A126D: R5223.2, R5224.1, U5207.12 (+)
XDC28EE8BE69FDEE96DB6: C5207.1, R5238.1, U5209.1
XDD0D5B27FC5290C34657: R5244.1, U5205.16
XE140B213E9EDE790AFAE: R5247.1, U5207.6 (-), U5207.7
XE1537ACA21E2254964DF: R5250.2, R5251.2, U5209.13 (-)
XEA2171B53449ACE0D9D9: R5253.2, R5254.2, U5210.2 (-)
XEAB6ACB2026EFB6F4154: R5242.2, R5243.1, U5205.3 (+)
XF6C3F0A1BE4E8B3E1441: U5206.13 (-), U5206.14
XF49F726E504854D63E19: D5206.2 (A), D5207.1 (K), R5252.2, U5210.3 (+)
XF66CDA4C7BD039CA904A: R5269.1
