Takazudo/zudo-osc-hole-field/boards/osc-core/sheets/wavefolder_W2_K.kicad_sch

## KiCad design boards/osc-core/sheets/wavefolder_W2_K.kicad_sch (2026-10-05)

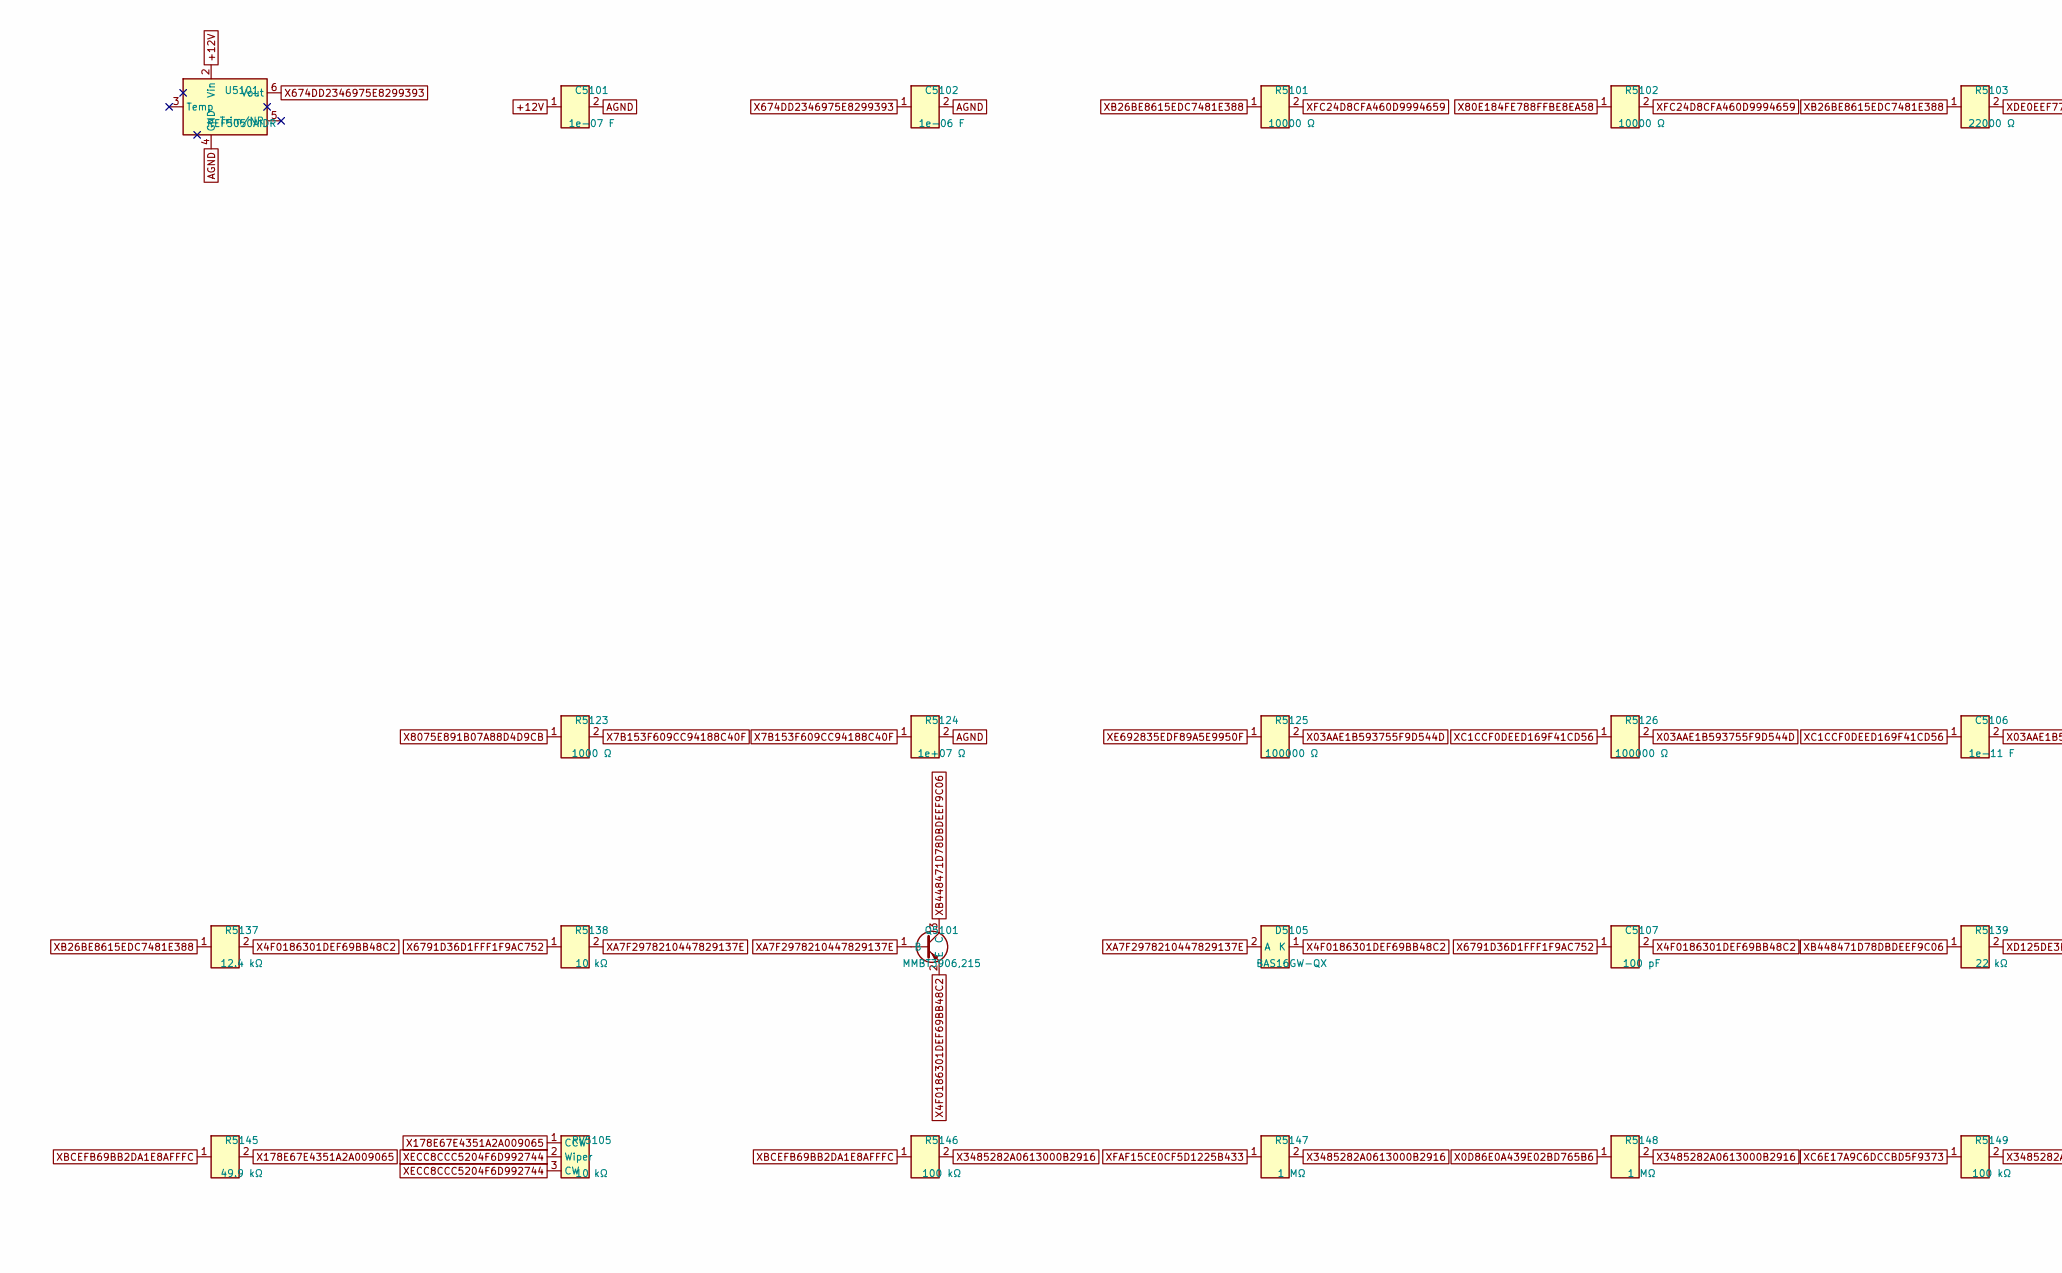
[picture p193: schematic wavefolder_W2_K.kicad_sch, part in row 1, column 1]

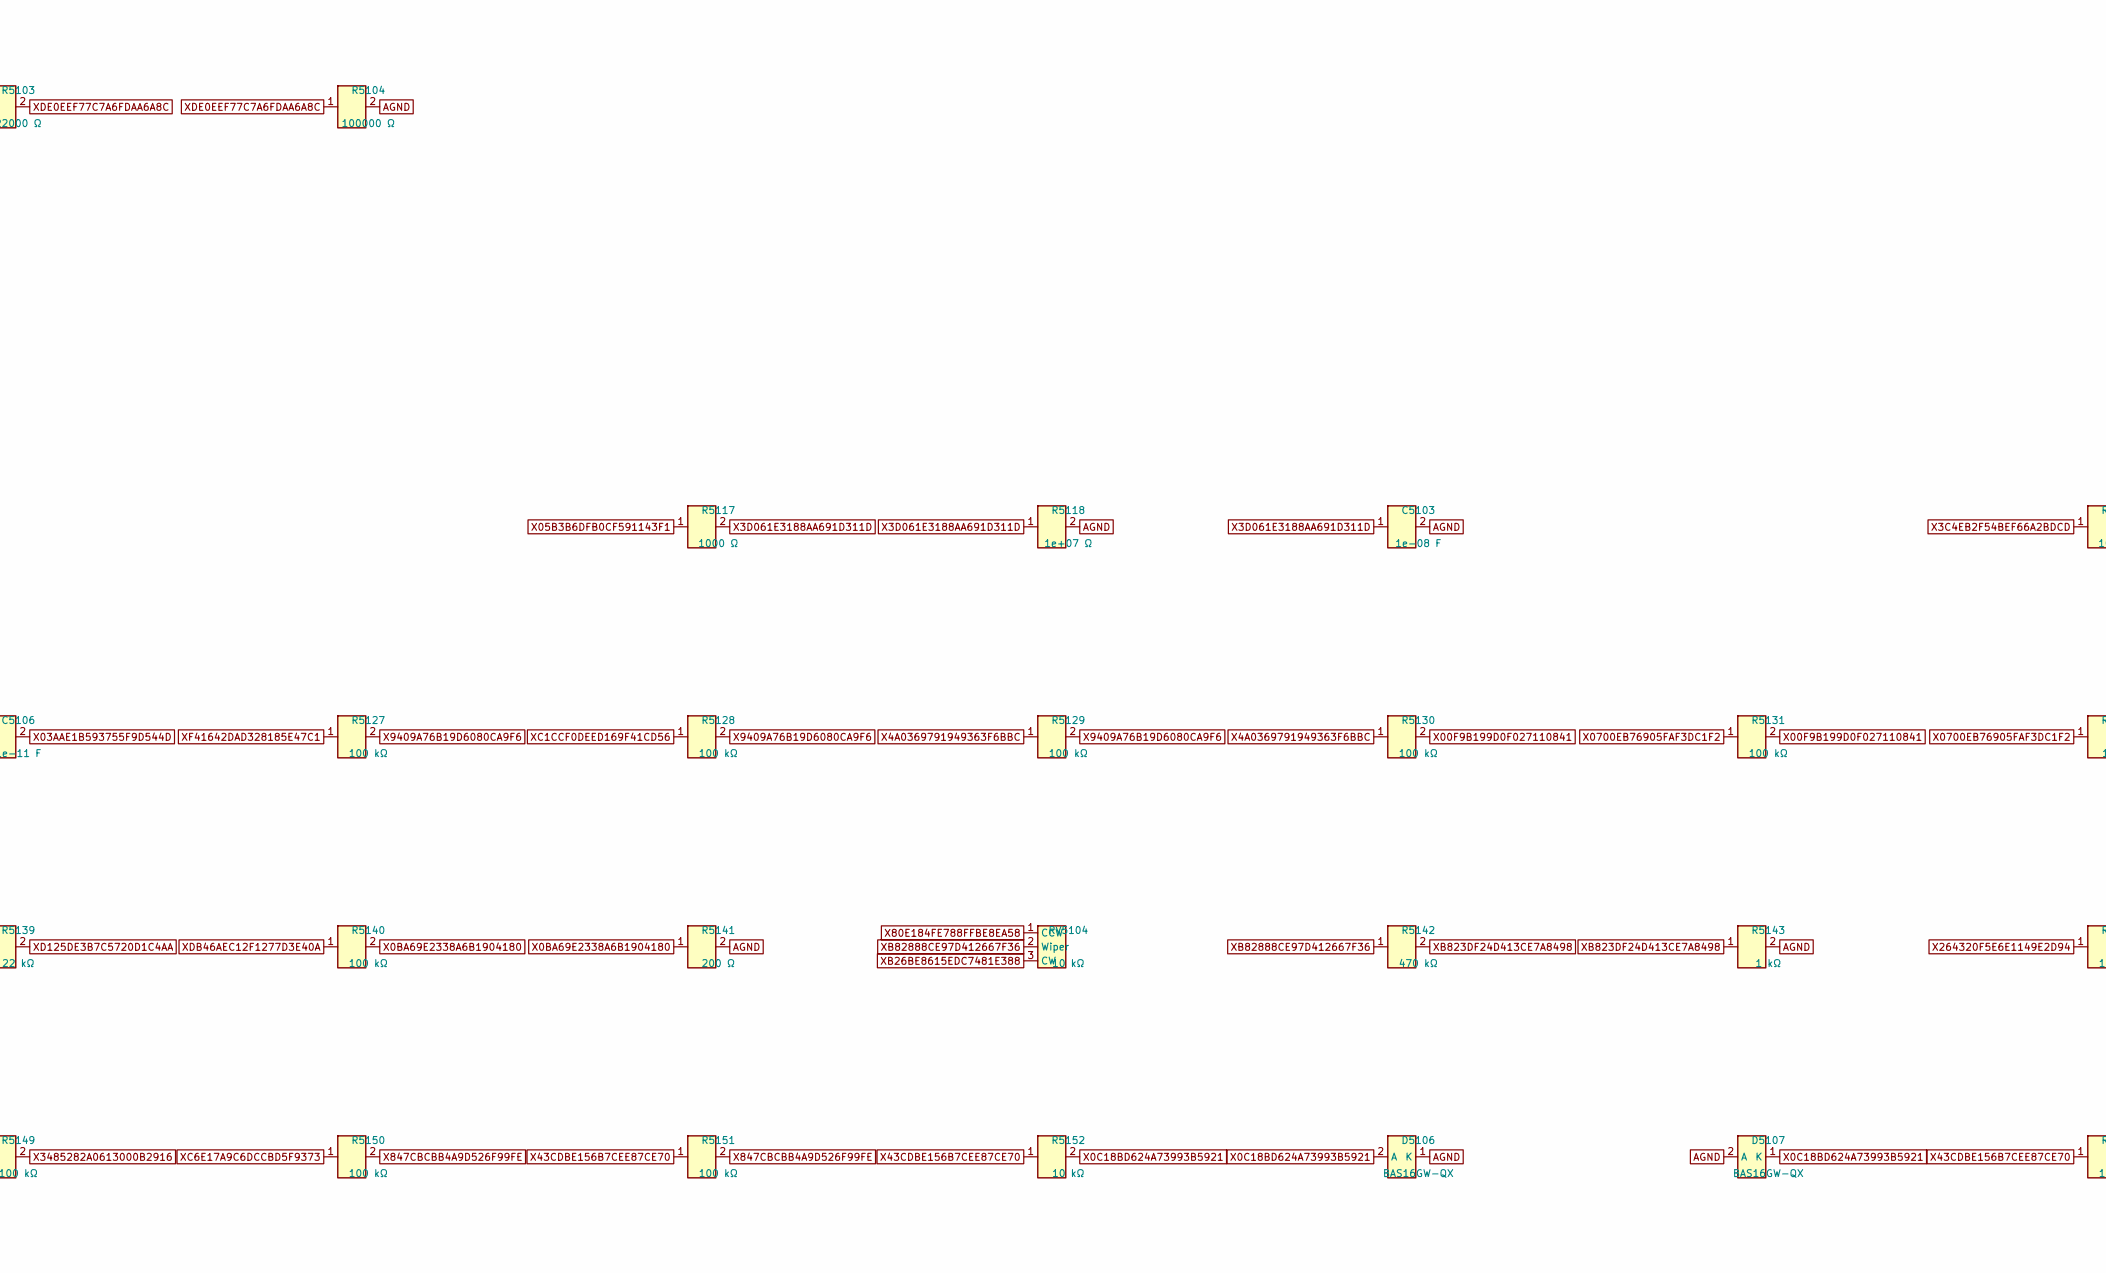
[picture p194: schematic wavefolder_W2_K.kicad_sch, part in row 1, column 2]

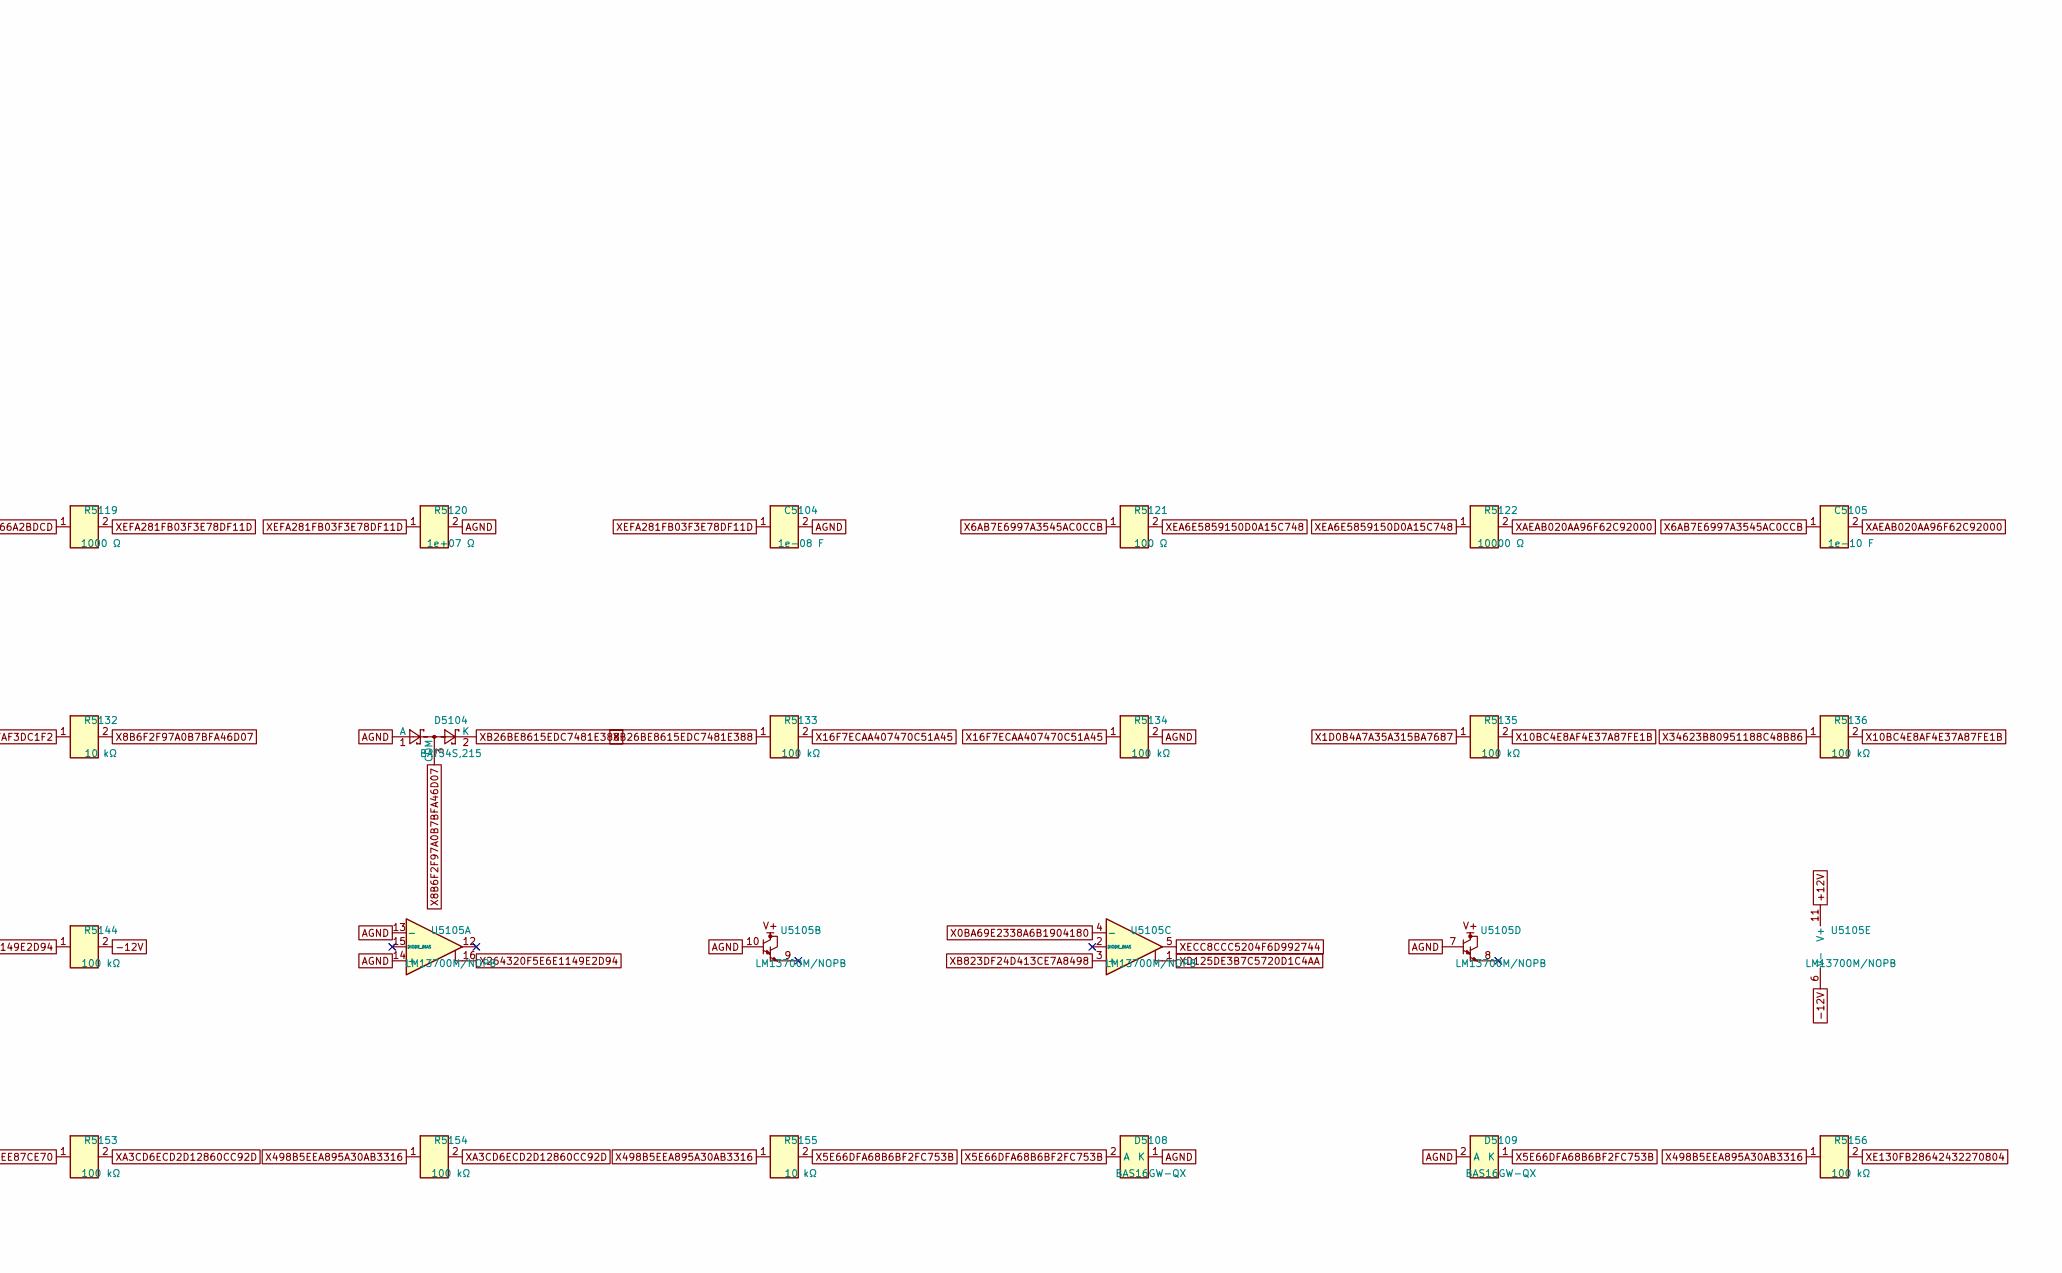
[picture p195: schematic wavefolder_W2_K.kicad_sch, part in row 1, column 3]

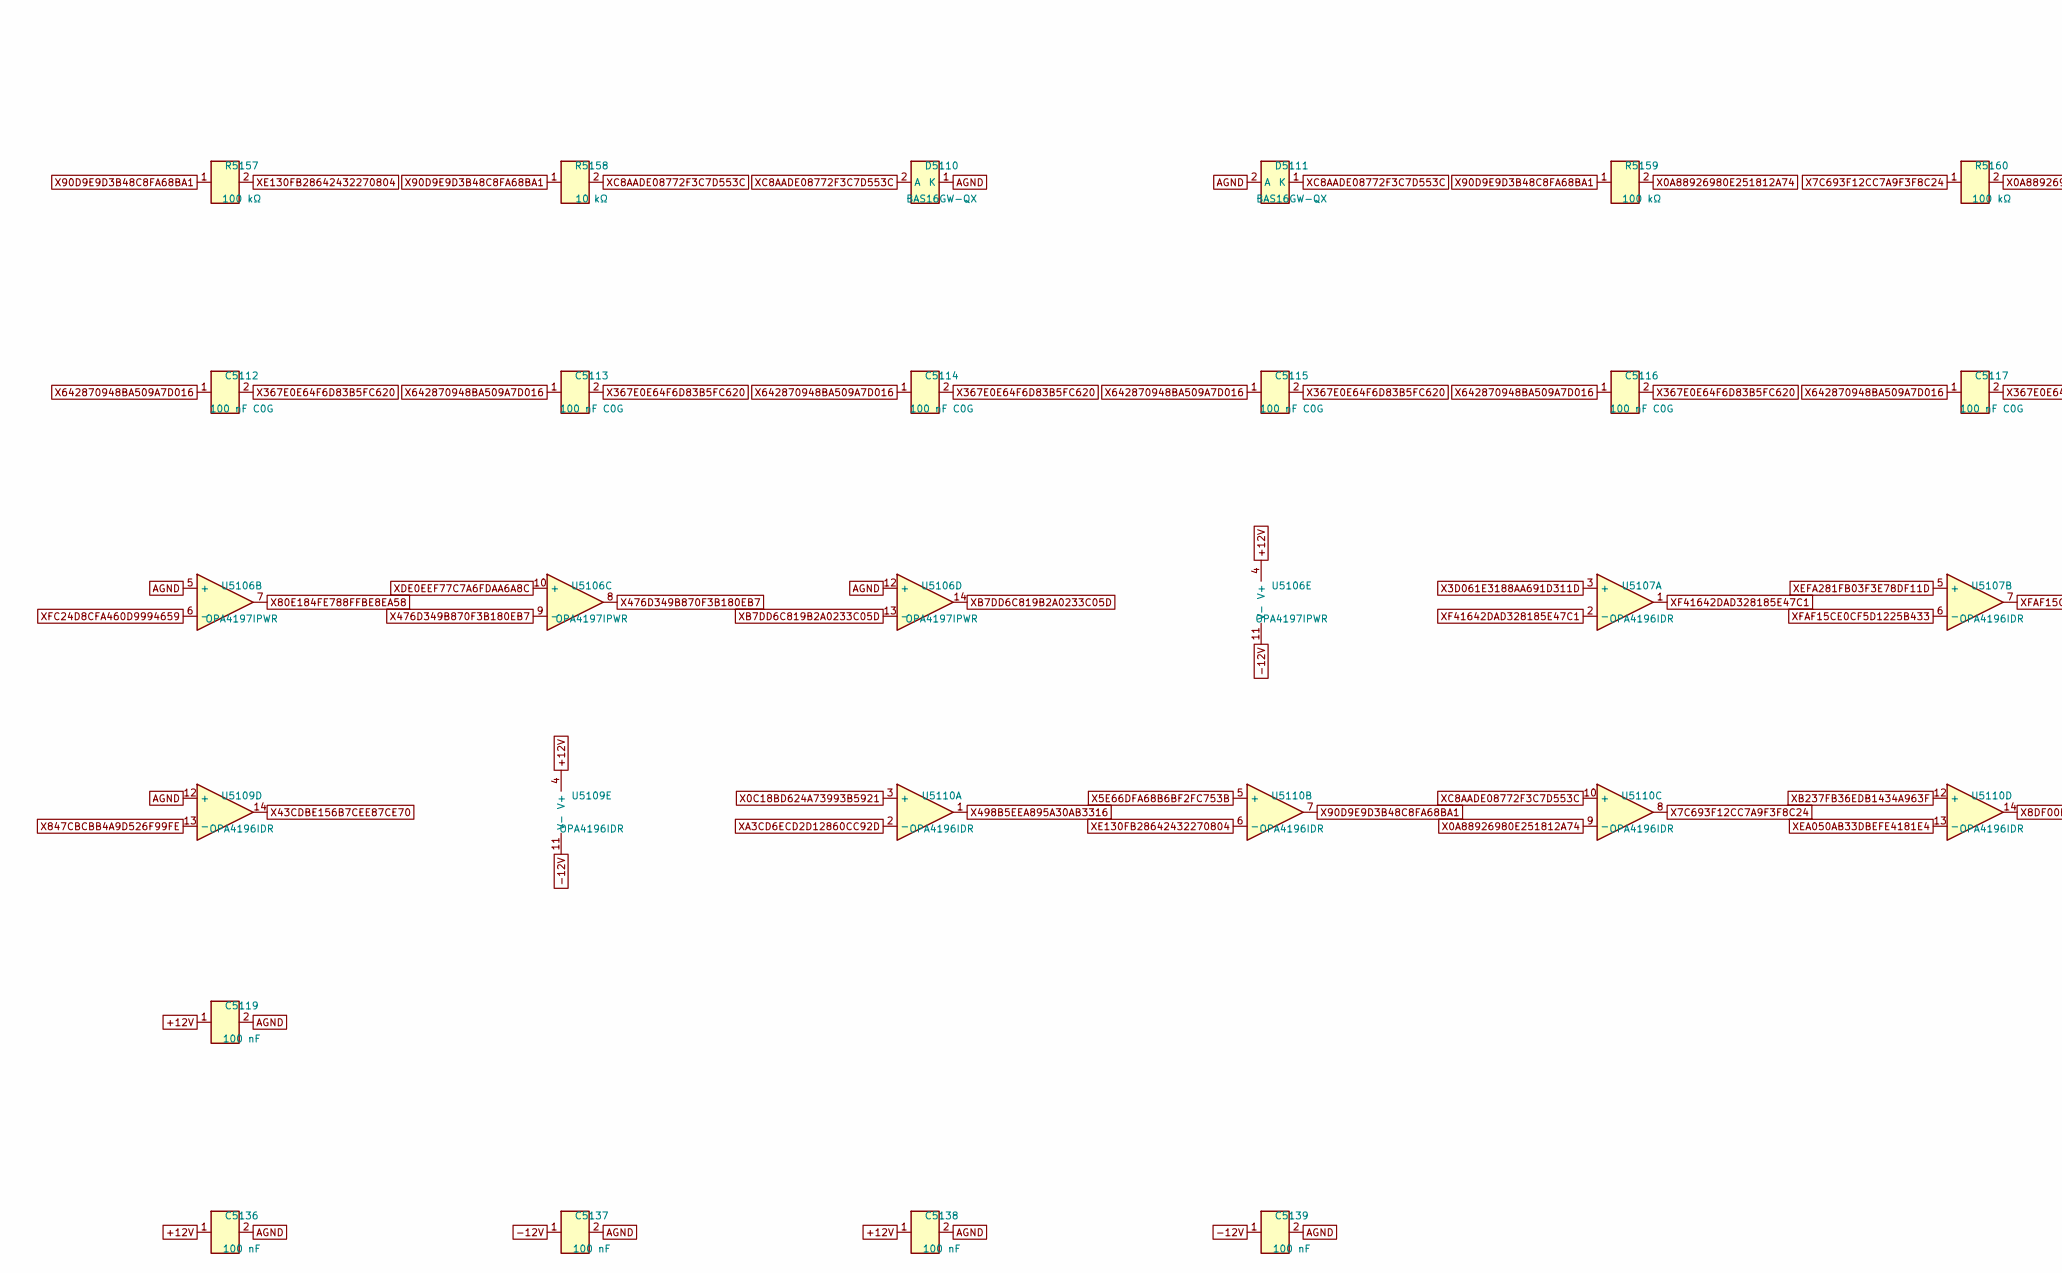
[picture p196: schematic wavefolder_W2_K.kicad_sch, part in row 2, column 1]

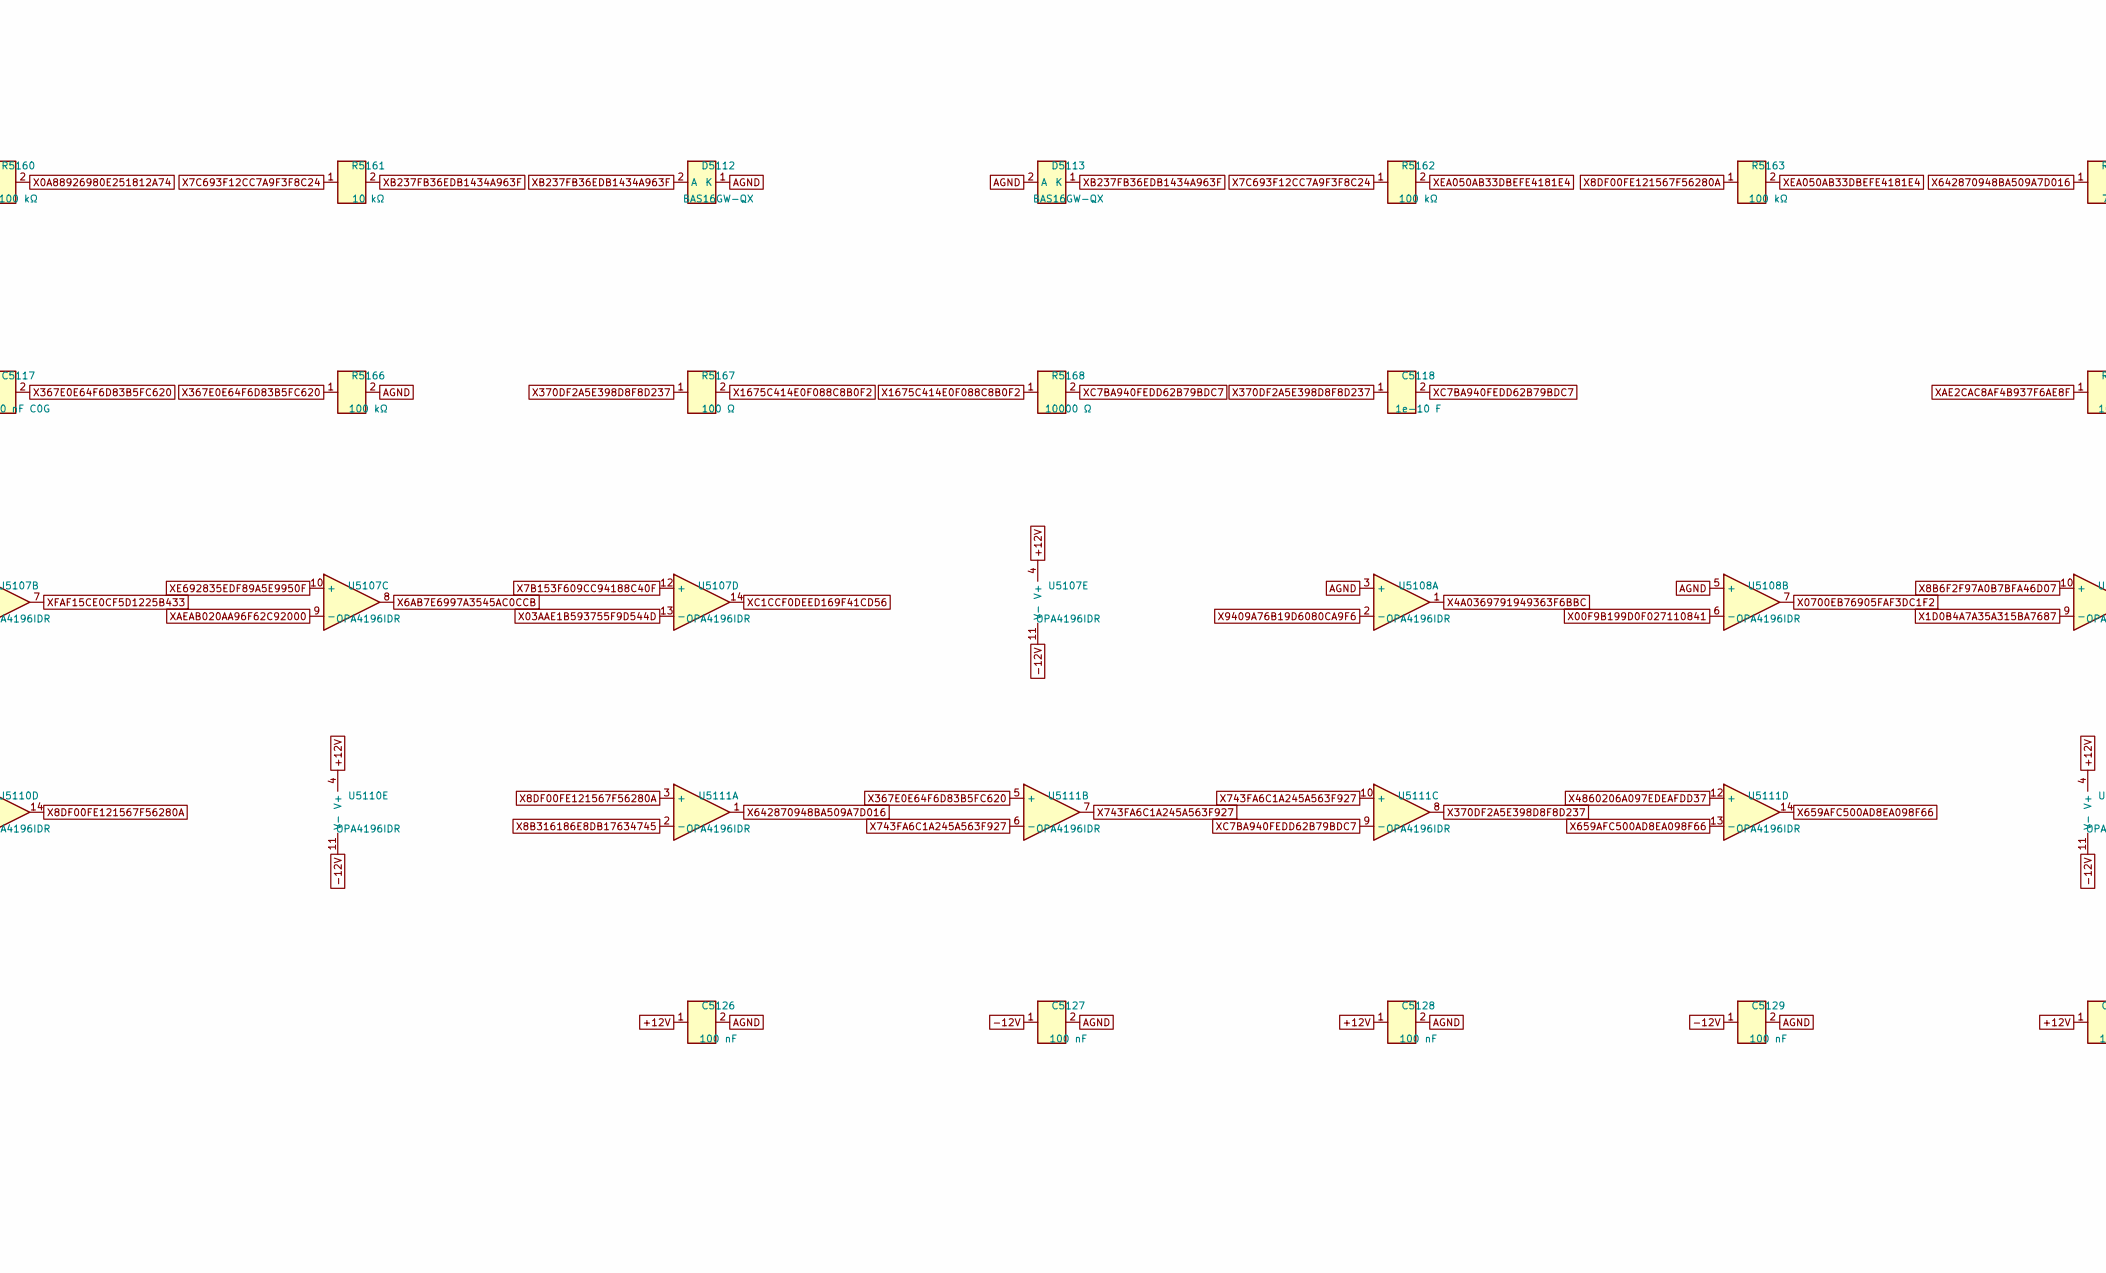
[picture p197: schematic wavefolder_W2_K.kicad_sch, part in row 2, column 2]

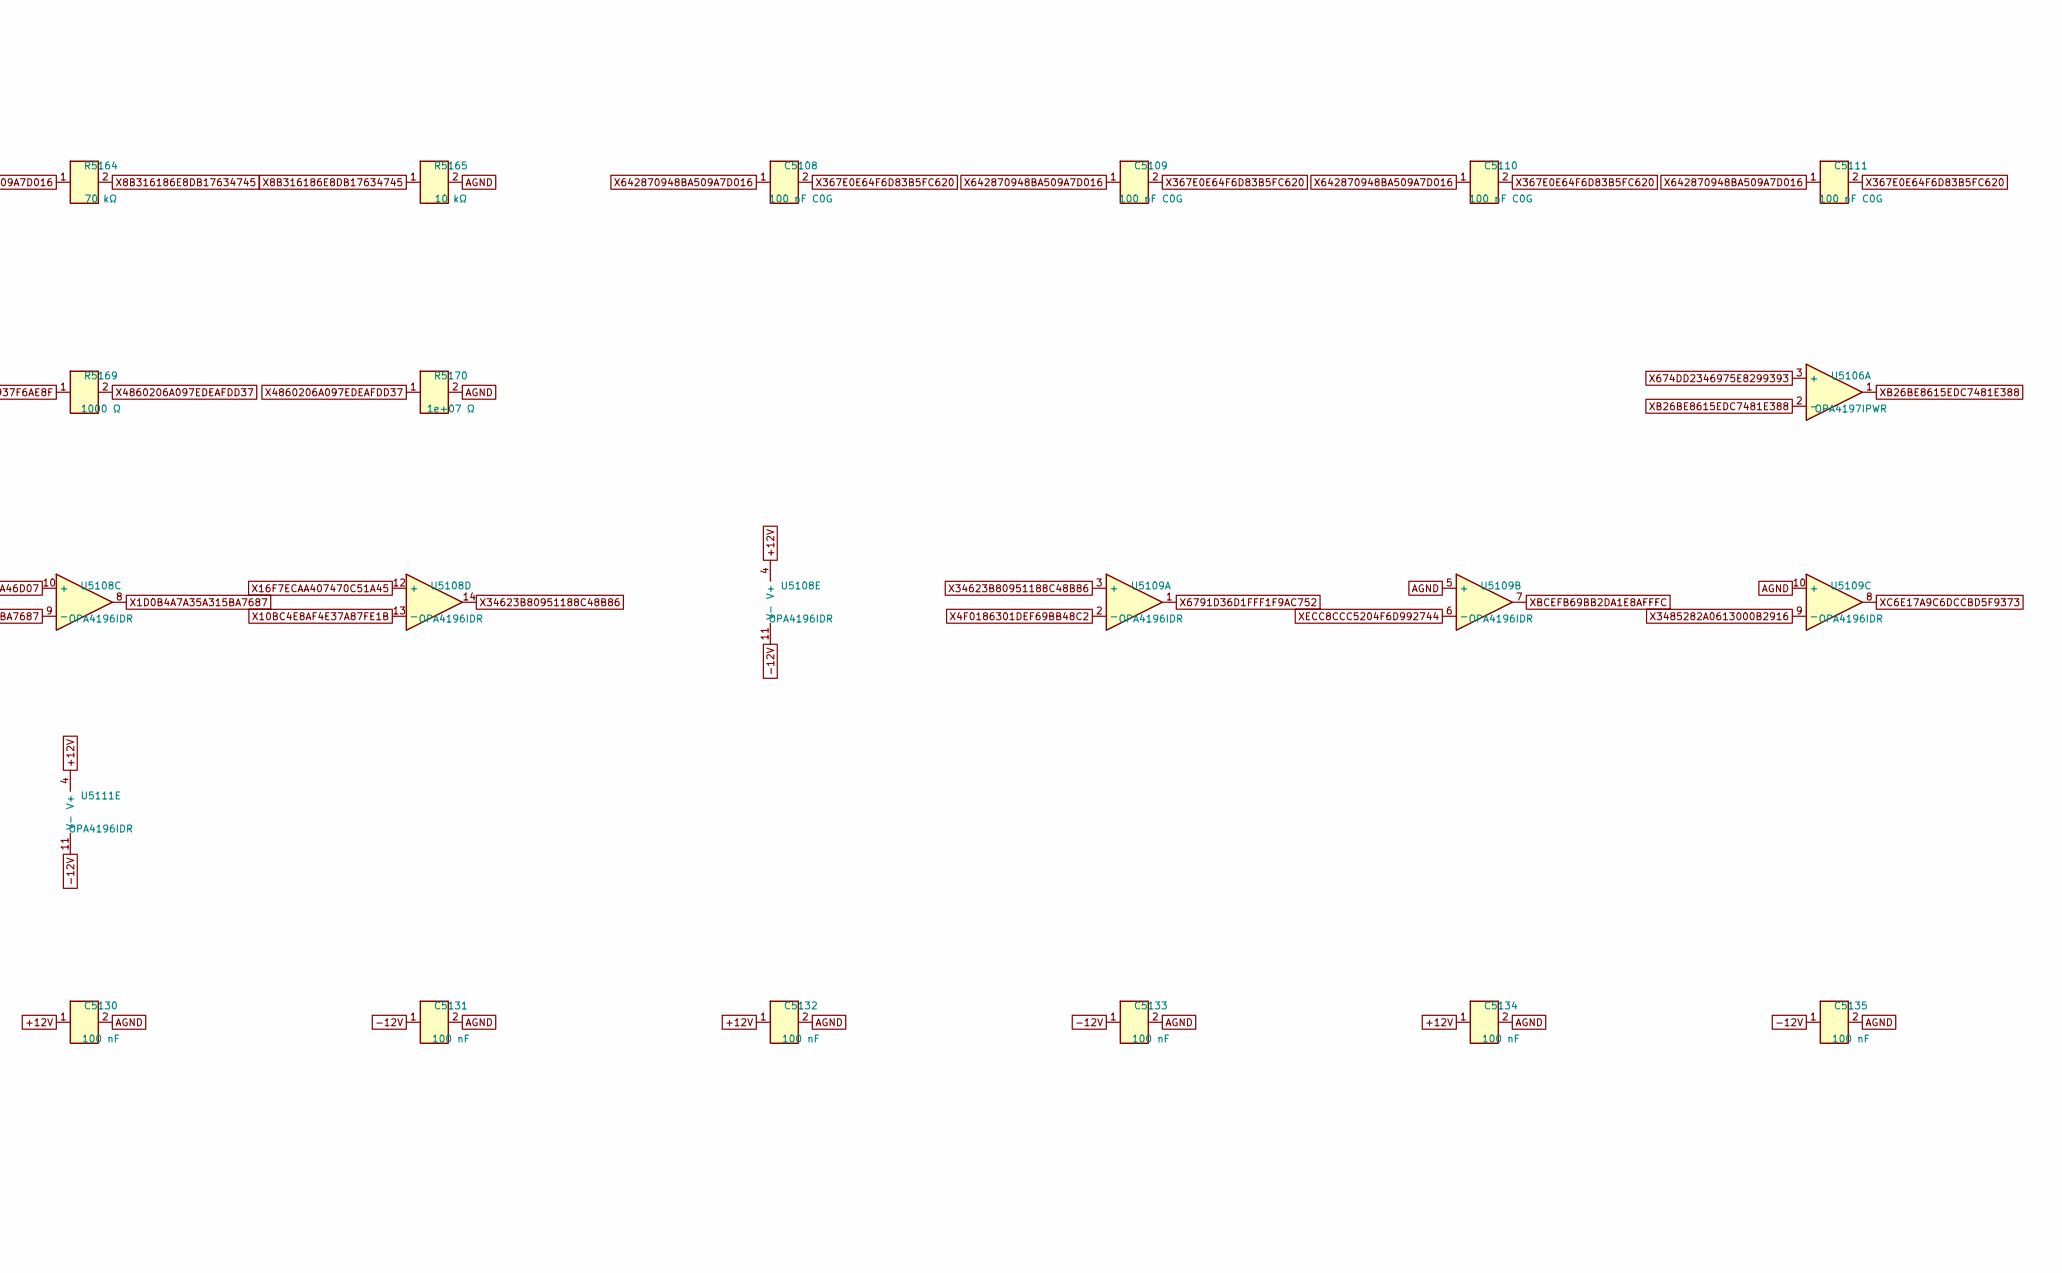
[picture p198: schematic wavefolder_W2_K.kicad_sch, part in row 2, column 3]

Parts:
C5101: 1e-07 F; C0603; MPN GRM188R71H104KA93D
C5102: 1e-06 F; C0603
C5103, C5104: 1e-08 F; C0603
C5105, C5118: 1e-10 F; C0603; MPN C0603C101J5GACTU
C5106: 1e-11 F; C0603
C5107: 100 pF; C0603; MPN C0603C101J5GACTU
C5108, C5109, C5110, C5111, C5112, C5113, C5114, C5115, C5116, C5117: 100 nF C0G; C1206; MPN 1206CG104J500NT; LCSC C46348
C5119, C5126, C5127, C5128, C5129, C5130, C5131, C5132, C5133, C5134, C5135, C5136, C5137, C5138, C5139: 100 nF; C0603; MPN GRM188R71H104KA93D
D5104: BAT54S,215; SOT-23; MPN BAT54S,215
D5105, D5106, D5107, D5108, D5109, D5110, D5111, D5112, D5113: BAS16GW-QX; SOD-123; MPN BAS16GW-QX
Q5101: MMBT3906,215; SOT-23; MPN MMBT3906,215
R5101, R5102, R5122, R5168: 10000 Ω; R0603
R5103: 22000 Ω; R0603
R5104, R5125, R5126: 100000 Ω; R0603; MPN RT0603BRD07100KL
R5117, R5119, R5123, R5169: 1000 Ω; R0603
R5118, R5120, R5124, R5170: 1e+07 Ω; R0603
R5121, R5167: 100 Ω; R0603
R5127, R5128, R5129, R5130, R5131, R5133, R5134, R5135, R5136, R5140, R5144, R5146, R5149, R5150, R5151, R5153, R5154, R5156, R5157, R5159, R5160, R5162, R5163, R5166: 100 kΩ; R0603; MPN RT0603BRD07100KL
R5132, R5138, R5152, R5155, R5158, R5161, R5165: 10 kΩ; R0603
R5137: 12.4 kΩ; R0603
R5139: 22 kΩ; R0603
R5141: 200 Ω; R0603
R5142: 470 kΩ; R0603
R5143: 1 kΩ; R0603
R5145: 49.9 kΩ; R0603
R5147, R5148: 1 MΩ; R0603
R5164: 70 kΩ; R0603
RV5104, RV5105: 10 kΩ; Potentiometer_Bourns_TC33X_Vertical; MPN TC33X-2-103E
U5101: REF5050AIDR; SOIC-8_3.9x4.9mm_P1.27mm; MPN REF5050AIDR; LCSC C27804
U5105: LM13700M/NOPB; SOIC-16_3.9x9.9mm_P1.27mm; MPN LM13700M/NOPB; LCSC C1346265
U5106: OPA4197IPWR; TSSOP-14_4.4x5mm_P0.65mm; MPN OPA4197IPWR; LCSC C2057327
U5107, U5108, U5109, U5110, U5111: OPA4196IDR; SOIC-14_3.9x8.7mm_P1.27mm; MPN OPA4196IDR; LCSC C2057385

Connections:
+12V: C5101.1, C5119.1, C5126.1, C5128.1, C5130.1, C5132.1, C5134.1, C5136.1, C5138.1, U5101.2 (Vin), U5105.11 (V+), U5106.4 (V+), U5107.4 (V+), U5108.4 (V+), U5109.4 (V+), U5110.4 (V+), U5111.4 (V+)
-12V: C5127.1, C5129.1, C5131.1, C5133.1, C5135.1, C5137.1, C5139.1, R5144.2, U5105.6 (V-), U5106.11 (V-), U5107.11 (V-), U5108.11 (V-), U5109.11 (V-), U5110.11 (V-), U5111.11 (V-)
AGND: C5101.2, C5102.2, C5103.2, C5104.2, C5119.2, C5126.2, C5127.2, C5128.2, C5129.2, C5130.2, C5131.2, C5132.2, C5133.2, C5134.2, C5135.2, C5136.2, C5137.2, C5138.2, C5139.2, D5104.1 (A), D5106.1 (K), D5107.2 (A), D5108.1 (K), D5109.2 (A), D5110.1 (K), D5111.2 (A), D5112.1 (K), D5113.2 (A), R5104.2, R5118.2, R5120.2, R5124.2, R5134.2, R5141.2, R5143.2, R5165.2, R5166.2, R5170.2, U5101.4 (GND), U5105.7, U5105.10, U5105.13 (-), U5105.14 (+), U5106.5 (+), U5106.12 (+), U5108.3 (+), U5108.5 (+), U5109.5 (+), U5109.10 (+), U5109.12 (+)
X0A88926980E251812A74: R5159.2, R5160.2, U5110.9 (-)
X0BA69E2338A6B1904180: R5140.2, R5141.1, U5105.4 (-)
X0C18BD624A73993B5921: D5106.2 (A), D5107.1 (K), R5152.2, U5110.3 (+)
X0D86E0A439E02BD765B6: R5148.1
X00F9B199D0F027110841: R5130.2, R5131.2, U5108.6 (-)
X1D0B4A7A35A315BA7687: R5135.1, U5108.8, U5108.9 (-)
X03AAE1B593755F9D544D: C5106.2, R5125.2, R5126.2, U5107.13 (-)
X3C4EB2F54BEF66A2BDCD: R5119.1
X3D061E3188AA691D311D: C5103.1, R5117.2, R5118.1, U5107.3 (+)
X4A0369791949363F6BBC: R5129.1, R5130.1, U5108.1
X4F0186301DEF69BB48C2: C5107.2, D5105.1 (K), Q5101.2 (E), R5137.2, U5109.2 (-)
X05B3B6DFB0CF591143F1: R5117.1
X5E66DFA68B6BF2FC753B: D5108.2 (A), D5109.1 (K), R5155.2, U5110.5 (+)
X6AB7E6997A3545AC0CCB: C5105.1, R5121.1, U5107.8
X7B153F609CC94188C40F: R5123.2, R5124.1, U5107.12 (+)
X7C693F12CC7A9F3F8C24: R5160.1, R5161.1, R5162.1, U5110.8
X8B6F2F97A0B7BFA46D07: D5104.3 (COM), R5132.2, U5108.10 (+)
X8B316186E8DB17634745: R5164.2, R5165.1, U5111.2 (-)
X8DF00FE121567F56280A: R5163.1, U5110.14, U5111.3 (+)
X10BC4E8AF4E37A87FE1B: R5135.2, R5136.2, U5108.13 (-)
X16F7ECAA407470C51A45: R5133.2, R5134.1, U5108.12 (+)
X43CDBE156B7CEE87CE70: R5151.1, R5152.1, R5153.1, U5109.14
X80E184FE788FFBE8EA58: R5102.1, RV5104.1 (CCW), U5106.7
X90D9E9D3B48C8FA68BA1: R5157.1, R5158.1, R5159.1, U5110.7
X178E67E4351A2A009065: R5145.2, RV5105.1 (CCW)
X367E0E64F6D83B5FC620: C5108.2, C5109.2, C5110.2, C5111.2, C5112.2, C5113.2, C5114.2, C5115.2, C5116.2, C5117.2, R5166.1, U5111.5 (+)
X370DF2A5E398D8F8D237: C5118.1, R5167.1, U5111.8
X476D349B870F3B180EB7: U5106.8, U5106.9 (-)
X498B5EEA895A30AB3316: R5154.1, R5155.1, R5156.1, U5110.1
X659AFC500AD8EA098F66: U5111.13 (-), U5111.14
X674DD2346975E8299393: C5102.1, U5101.6 (Vout), U5106.3 (+)
X0700EB76905FAF3DC1F2: R5131.1, R5132.1, U5108.7
X743FA6C1A245A563F927: U5111.6 (-), U5111.7, U5111.10 (+)
X847CBCBB4A9D526F99FE: R5150.2, R5151.2, U5109.13 (-)
X1675C414E0F088C8B0F2: R5167.2, R5168.1
X6791D36D1FFF1F9AC752: C5107.1, R5138.1, U5109.1
X8075E891B07A88D4D9CB: R5123.1
X9409A76B19D6080CA9F6: R5127.2, R5128.2, R5129.2, U5108.2 (-)
X34623B80951188C48B86: R5136.1, U5108.14, U5109.3 (+)
X264320F5E6E1149E2D94: R5144.1, U5105.16
X3485282A0613000B2916: R5146.2, R5147.2, R5148.2, R5149.2, U5109.9 (-)
X4860206A097EDEAFDD37: R5169.2, R5170.1, U5111.12 (+)
X642870948BA509A7D016: C5108.1, C5109.1, C5110.1, C5111.1, C5112.1, C5113.1, C5114.1, C5115.1, C5116.1, C5117.1, R5164.1, U5111.1
XA3CD6ECD2D12860CC92D: R5153.2, R5154.2, U5110.2 (-)
XA7F2978210447829137E: D5105.2 (A), Q5101.1 (B), R5138.2
XAE2CAC8AF4B937F6AE8F: R5169.1
XAEAB020AA96F62C92000: C5105.2, R5122.2, U5107.9 (-)
XB7DD6C819B2A0233C05D: U5106.13 (-), U5106.14
XB26BE8615EDC7481E388: D5104.2 (K), R5101.1, R5103.1, R5133.1, R5137.1, RV5104.3 (CW), U5106.1, U5106.2 (-)
XB237FB36EDB1434A963F: D5112.2 (A), D5113.1 (K), R5161.2, U5110.12 (+)
XB823DF24D413CE7A8498: R5142.2, R5143.1, U5105.3 (+)
XB82888CE97D412667F36: R5142.1, RV5104.2 (Wiper)
XB448471D78DBDEEF9C06: Q5101.3 (C), R5139.1
XBCEFB69BB2DA1E8AFFFC: R5145.1, R5146.1, U5109.7
XC1CCF0DEED169F41CD56: C5106.1, R5126.1, R5128.1, U5107.14
XC6E17A9C6DCCBD5F9373: R5149.1, R5150.1, U5109.8
XC7BA940FEDD62B79BDC7: C5118.2, R5168.2, U5111.9 (-)
XC8AADE08772F3C7D553C: D5110.2 (A), D5111.1 (K), R5158.2, U5110.10 (+)
XD125DE3B7C5720D1C4AA: R5139.2, U5105.1
XDB46AEC12F1277D3E40A: R5140.1
XDE0EEF77C7A6FDAA6A8C: R5103.2, R5104.1, U5106.10 (+)
XE130FB28642432270804: R5156.2, R5157.2, U5110.6 (-)
XE692835EDF89A5E9950F: R5125.1, U5107.10 (+)
XEA6E5859150D0A15C748: R5121.2, R5122.1
XEA050AB33DBEFE4181E4: R5162.2, R5163.2, U5110.13 (-)
XECC8CCC5204F6D992744: RV5105.2 (Wiper), RV5105.3 (CW), U5105.5, U5109.6 (-)
XEFA281FB03F3E78DF11D: C5104.1, R5119.2, R5120.1, U5107.5 (+)
XF41642DAD328185E47C1: R5127.1, U5107.1, U5107.2 (-)
XFAF15CE0CF5D1225B433: R5147.1, U5107.6 (-), U5107.7
XFC24D8CFA460D9994659: R5101.2, R5102.2, U5106.6 (-)
