Takazudo/zudo-osc-hole-field/schematic/cells/sheets/bipolar_attenuverter.kicad_sch

## KiCad design schematic/cells/sheets/bipolar_attenuverter.kicad_sch (2026-09-30)

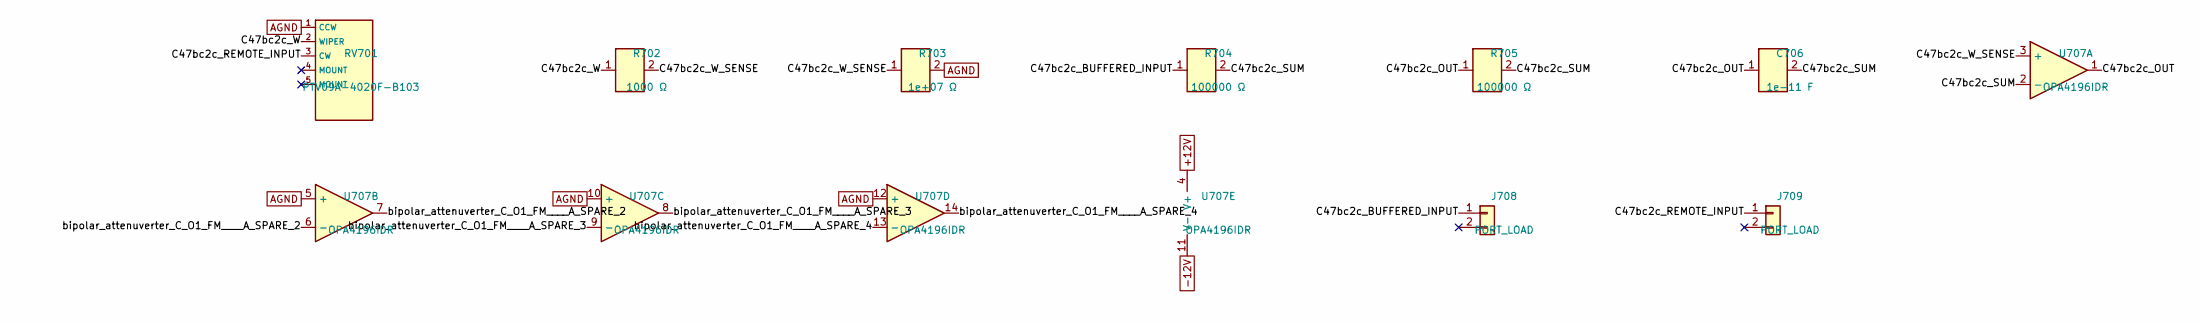
[picture p199: schematic bipolar_attenuverter.kicad_sch]

Parts:
C706: 1e-11 F; C0603
J708, J709: PORT_LOAD
R702: 1000 Ω; R0603
R703: 1e+07 Ω; R0603
R704, R705: 100000 Ω; R0603; MPN RT0603BRD07100KL
RV701: PTV09A-4020F-B103; PTV09A-4020F; MPN PTV09A-4020F-B103; LCSC C5848782
U707: OPA4196IDR; SOIC-14_3.9x8.7mm_P1.27mm; MPN OPA4196IDR; LCSC C2057385

Connections:
+12V: U707.4 (V+)
-12V: U707.11 (V-)
AGND: R703.2, RV701.1 (CCW), U707.5 (+), U707.10 (+), U707.12 (+)
C47bc2c_BUFFERED_INPUT: J708.1, R704.1
C47bc2c_OUT: C706.1, R705.1, U707.1
C47bc2c_REMOTE_INPUT: J709.1, RV701.3 (CW)
C47bc2c_SUM: C706.2, R704.2, R705.2, U707.2 (-)
C47bc2c_W: R702.1, RV701.2 (WIPER)
C47bc2c_W_SENSE: R702.2, R703.1, U707.3 (+)
bipolar_attenuverter_C_O1_FM____A_SPARE_2: U707.6 (-), U707.7
bipolar_attenuverter_C_O1_FM____A_SPARE_3: U707.8, U707.9 (-)
bipolar_attenuverter_C_O1_FM____A_SPARE_4: U707.13 (-), U707.14
