Takazudo/zudo-osc-hole-field/schematic/cells/sheets/clip_detector.kicad_sch

## KiCad design schematic/cells/sheets/clip_detector.kicad_sch (2026-09-30)

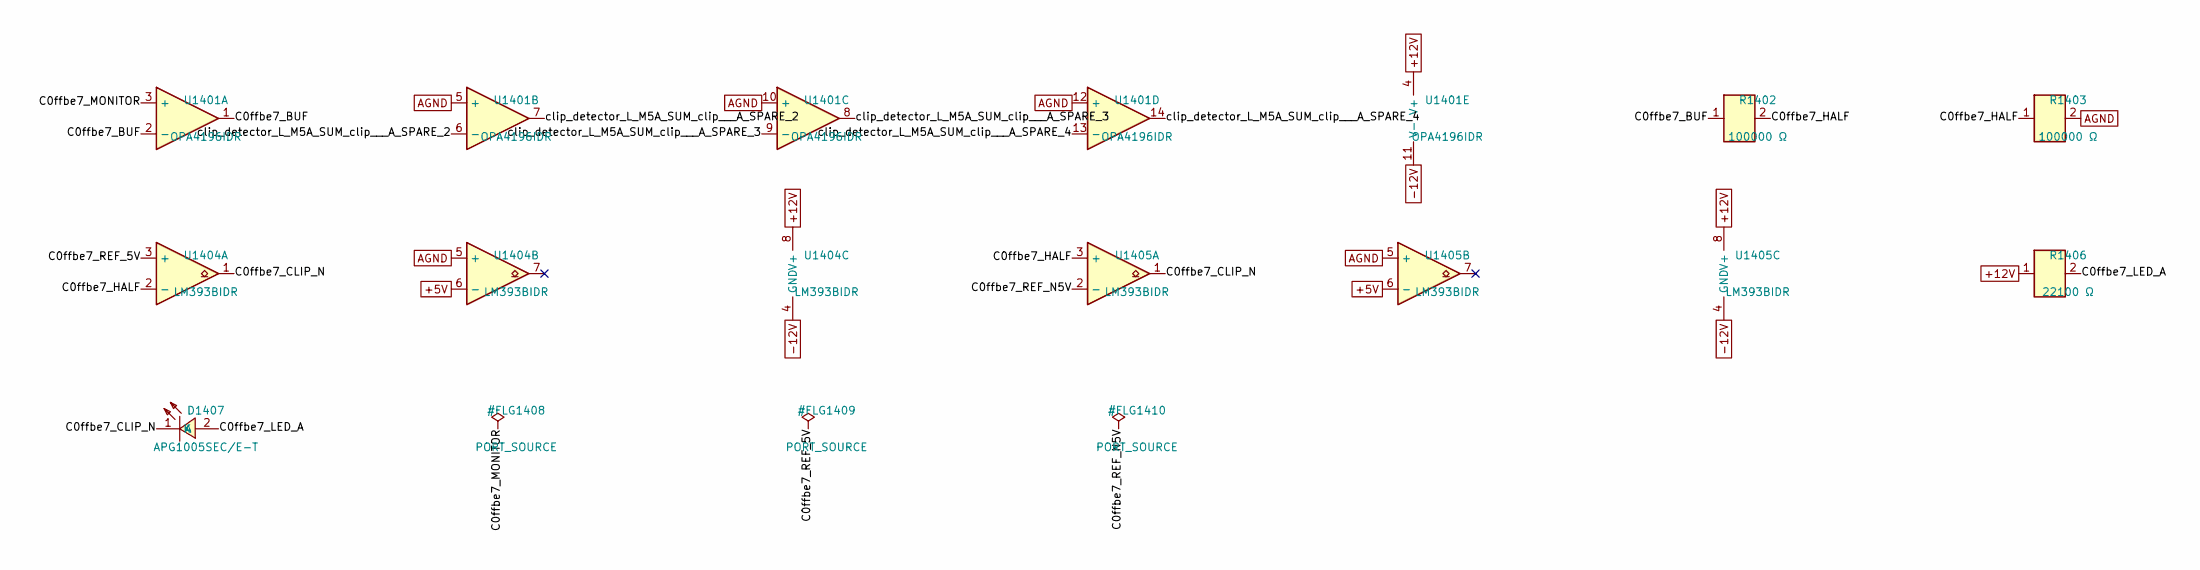
[picture p200: schematic clip_detector.kicad_sch]

Parts:
D1407: APG1005SEC/E-T; LED0402-Kingbright-Red; MPN APG1005SEC/E-T
R1402, R1403: 100000 Ω; R0603; MPN RT0603BRD07100KL
R1406: 22100 Ω; R0603
U1401: OPA4196IDR; SOIC-14_3.9x8.7mm_P1.27mm; MPN OPA4196IDR; LCSC C2057385
U1404, U1405: LM393BIDR; SOIC-8_3.9x4.9mm_P1.27mm; MPN LM393BIDR

Connections:
+5V: U1404.6 (-), U1405.6 (-)
+12V: R1406.1, U1401.4 (V+), U1404.8 (V+), U1405.8 (V+)
-12V: U1401.11 (V-), U1404.4 (GND), U1405.4 (GND)
AGND: R1403.2, U1401.5 (+), U1401.10 (+), U1401.12 (+), U1404.5 (+), U1405.5 (+)
C0ffbe7_BUF: R1402.1, U1401.1, U1401.2 (-)
C0ffbe7_CLIP_N: D1407.1 (K), U1404.1, U1405.1
C0ffbe7_HALF: R1402.2, R1403.1, U1404.2 (-), U1405.3 (+)
C0ffbe7_LED_A: D1407.2 (A), R1406.2
C0ffbe7_MONITOR: U1401.3 (+)
C0ffbe7_REF_5V: U1404.3 (+)
C0ffbe7_REF_N5V: U1405.2 (-)
clip_detector_L_M5A_SUM_clip___A_SPARE_2: U1401.6 (-), U1401.7
clip_detector_L_M5A_SUM_clip___A_SPARE_3: U1401.8, U1401.9 (-)
clip_detector_L_M5A_SUM_clip___A_SPARE_4: U1401.13 (-), U1401.14
