Takazudo/zudo-osc-hole-field/schematic/cells/sheets/dc_control_source.kicad_sch

## KiCad design schematic/cells/sheets/dc_control_source.kicad_sch (2026-09-30)

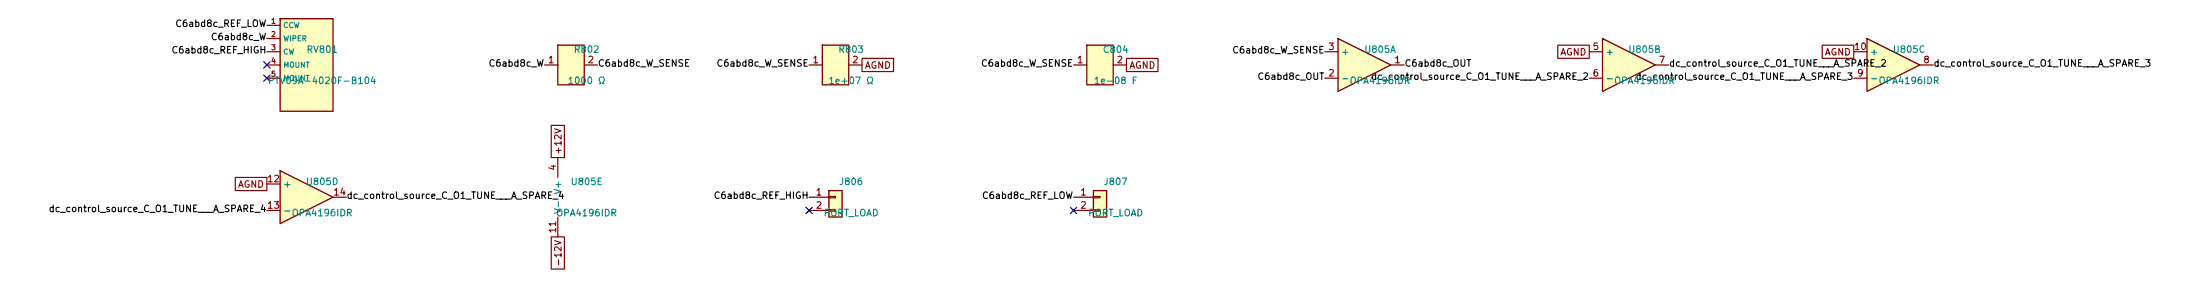
[picture p201: schematic dc_control_source.kicad_sch]

Parts:
C804: 1e-08 F; C0603
J806, J807: PORT_LOAD
R802: 1000 Ω; R0603
R803: 1e+07 Ω; R0603
RV801: PTV09A-4020F-B104; PTV09A-4020F; MPN PTV09A-4020F-B104
U805: OPA4196IDR; SOIC-14_3.9x8.7mm_P1.27mm; MPN OPA4196IDR; LCSC C2057385

Connections:
+12V: U805.4 (V+)
-12V: U805.11 (V-)
AGND: C804.2, R803.2, U805.5 (+), U805.10 (+), U805.12 (+)
C6abd8c_OUT: U805.1, U805.2 (-)
C6abd8c_REF_HIGH: J806.1, RV801.3 (CW)
C6abd8c_REF_LOW: J807.1, RV801.1 (CCW)
C6abd8c_W: R802.1, RV801.2 (WIPER)
C6abd8c_W_SENSE: C804.1, R802.2, R803.1, U805.3 (+)
dc_control_source_C_O1_TUNE___A_SPARE_2: U805.6 (-), U805.7
dc_control_source_C_O1_TUNE___A_SPARE_3: U805.8, U805.9 (-)
dc_control_source_C_O1_TUNE___A_SPARE_4: U805.13 (-), U805.14
