Takazudo/zudo-osc-hole-field/schematic/cells/sheets/decoupling_bulk.kicad_sch

## KiCad design schematic/cells/sheets/decoupling_bulk.kicad_sch (2026-09-30)

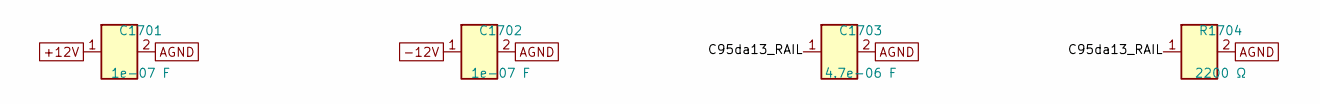
[picture p202: schematic decoupling_bulk.kicad_sch]

Parts:
C1701, C1702: 1e-07 F; C0603; MPN GRM188R71H104KA93D
C1703: 4.7e-06 F; C0805; MPN GRM21BR61E475KA12L
R1704: 2200 Ω; R0603

Connections:
+12V: C1701.1
-12V: C1702.1
AGND: C1701.2, C1702.2, C1703.2, R1704.2
C95da13_RAIL: C1703.1, R1704.1
