Takazudo/zudo-osc-hole-field/schematic/cells/sheets/gate_trigger_input.kicad_sch

## KiCad design schematic/cells/sheets/gate_trigger_input.kicad_sch (2026-09-30)

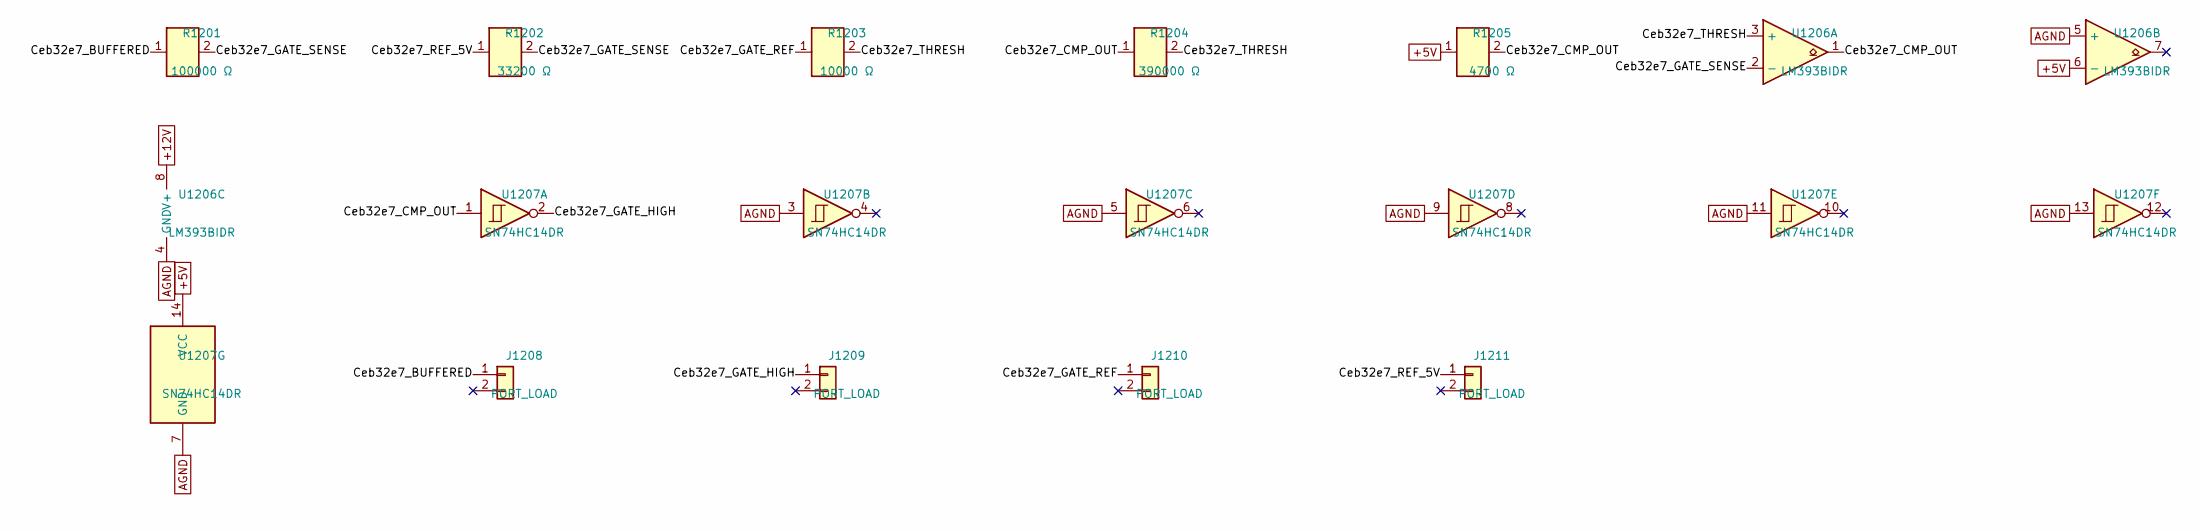
[picture p203: schematic gate_trigger_input.kicad_sch]

Parts:
J1208, J1209, J1210, J1211: PORT_LOAD
R1201: 100000 Ω; R0603; MPN RT0603BRD07100KL
R1202: 33200 Ω; R0603
R1203: 10000 Ω; R0603
R1204: 390000 Ω; R0603
R1205: 4700 Ω; R0603
U1206: LM393BIDR; SOIC-8_3.9x4.9mm_P1.27mm; MPN LM393BIDR
U1207: SN74HC14DR; SOIC-14_3.9x8.7mm_P1.27mm; MPN SN74HC14DR

Connections:
+5V: R1205.1, U1206.6 (-), U1207.14 (VCC)
+12V: U1206.8 (V+)
AGND: U1206.4 (GND), U1206.5 (+), U1207.3, U1207.5, U1207.7 (GND), U1207.9, U1207.11, U1207.13
Ceb32e7_BUFFERED: J1208.1, R1201.1
Ceb32e7_CMP_OUT: R1204.1, R1205.2, U1206.1, U1207.1
Ceb32e7_GATE_HIGH: J1209.1, U1207.2
Ceb32e7_GATE_REF: J1210.1, R1203.1
Ceb32e7_GATE_SENSE: R1201.2, R1202.2, U1206.2 (-)
Ceb32e7_REF_5V: J1211.1, R1202.1
Ceb32e7_THRESH: R1203.2, R1204.2, U1206.3 (+)
