Takazudo/zudo-osc-hole-field/schematic/cells/sheets/general_output.kicad_sch

## KiCad design schematic/cells/sheets/general_output.kicad_sch (2026-09-30)

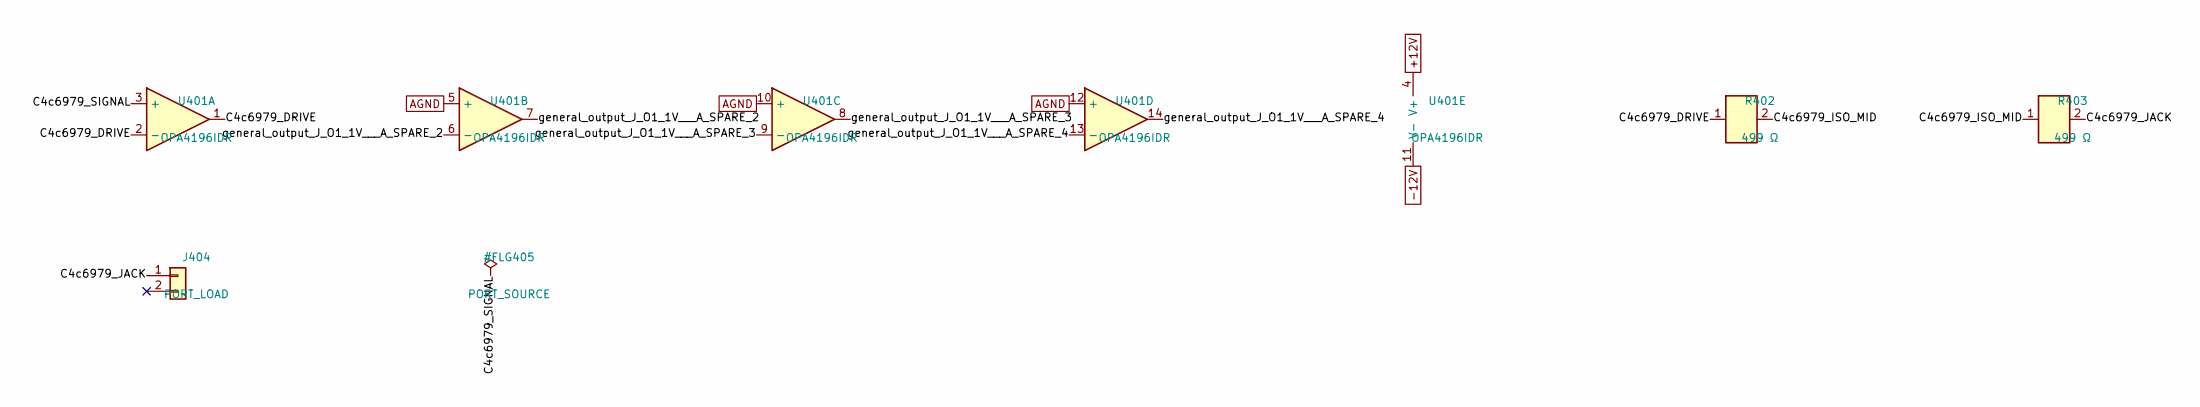
[picture p204: schematic general_output.kicad_sch]

Parts:
J404: PORT_LOAD
R402, R403: 499 Ω; R_1210_3225Metric; MPN RC1210FR-07499RL
U401: OPA4196IDR; SOIC-14_3.9x8.7mm_P1.27mm; MPN OPA4196IDR; LCSC C2057385

Connections:
+12V: U401.4 (V+)
-12V: U401.11 (V-)
AGND: U401.5 (+), U401.10 (+), U401.12 (+)
C4c6979_DRIVE: R402.1, U401.1, U401.2 (-)
C4c6979_ISO_MID: R402.2, R403.1
C4c6979_JACK: J404.1, R403.2
C4c6979_SIGNAL: U401.3 (+)
general_output_J_O1_1V___A_SPARE_2: U401.6 (-), U401.7
general_output_J_O1_1V___A_SPARE_3: U401.8, U401.9 (-)
general_output_J_O1_1V___A_SPARE_4: U401.13 (-), U401.14
