Takazudo/zudo-osc-hole-field/schematic/cells/sheets/high_impedance_input.kicad_sch

## KiCad design schematic/cells/sheets/high_impedance_input.kicad_sch (2026-09-30)

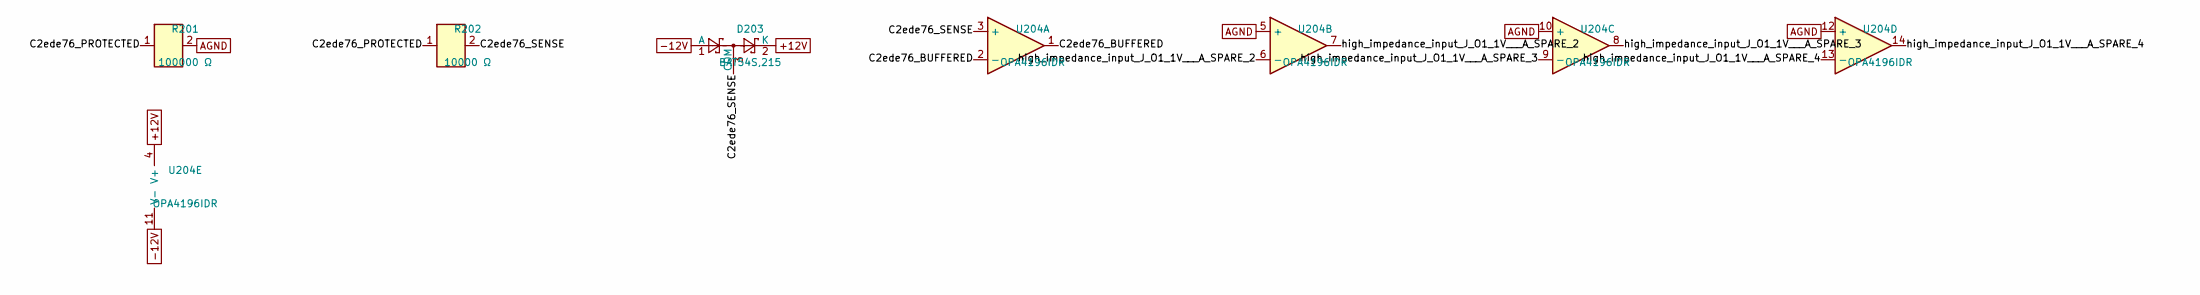
[picture p205: schematic high_impedance_input.kicad_sch]

Parts:
D203: BAT54S,215; SOT-23; MPN BAT54S,215
R201: 100000 Ω; R0603; MPN RC0603FR-07100KL
R202: 10000 Ω; R0603
U204: OPA4196IDR; SOIC-14_3.9x8.7mm_P1.27mm; MPN OPA4196IDR; LCSC C2057385

Connections:
+12V: D203.2 (K), U204.4 (V+)
-12V: D203.1 (A), U204.11 (V-)
AGND: R201.2, U204.5 (+), U204.10 (+), U204.12 (+)
C2ede76_BUFFERED: U204.1, U204.2 (-)
C2ede76_PROTECTED: R201.1, R202.1
C2ede76_SENSE: D203.3 (COM), R202.2, U204.3 (+)
high_impedance_input_J_O1_1V___A_SPARE_2: U204.6 (-), U204.7
high_impedance_input_J_O1_1V___A_SPARE_3: U204.8, U204.9 (-)
high_impedance_input_J_O1_1V___A_SPARE_4: U204.13 (-), U204.14
