Takazudo/zudo-osc-hole-field/schematic/cells/sheets/input_fault_switch.kicad_sch

## KiCad design schematic/cells/sheets/input_fault_switch.kicad_sch (2026-09-30)

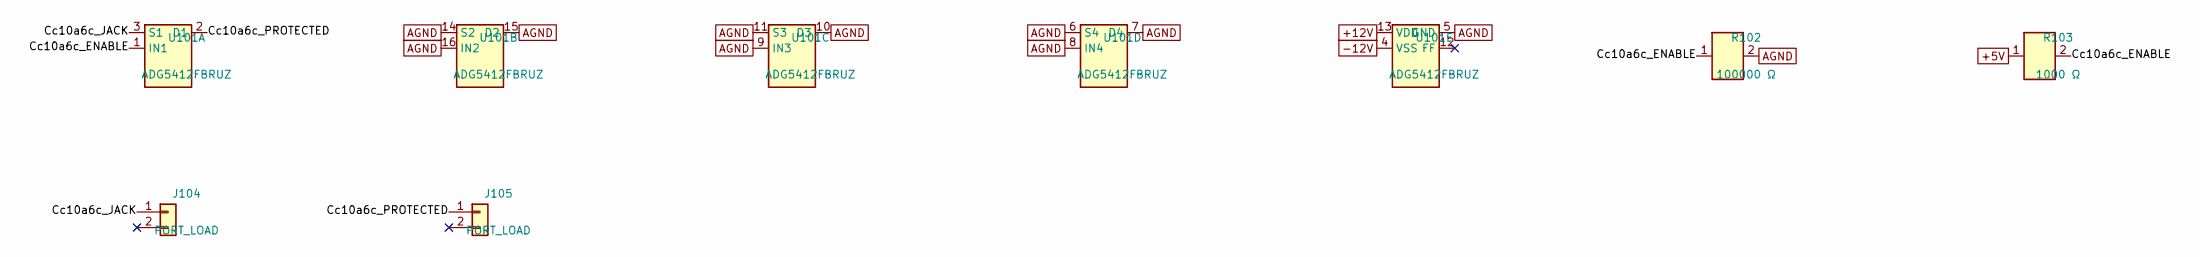
[picture p206: schematic input_fault_switch.kicad_sch]

Parts:
J104, J105: PORT_LOAD
R102: 100000 Ω; R0603; MPN RC0603FR-07100KL
R103: 1000 Ω; R0603
U101: ADG5412FBRUZ; TSSOP-16_4.4x5mm_P0.65mm; MPN ADG5412FBRUZ; LCSC C579073

Connections:
+5V: R103.1
+12V: U101.13 (VDD)
-12V: U101.4 (VSS)
AGND: R102.2, U101.5 (GND), U101.6 (S4), U101.7 (D4), U101.8 (IN4), U101.9 (IN3), U101.10 (D3), U101.11 (S3), U101.14 (S2), U101.15 (D2), U101.16 (IN2)
Cc10a6c_ENABLE: R102.1, R103.2, U101.1 (IN1)
Cc10a6c_JACK: J104.1, U101.3 (S1)
Cc10a6c_PROTECTED: J105.1, U101.2 (D1)
