Takazudo/zudo-osc-hole-field/schematic/cells/sheets/level_attenuator.kicad_sch

## KiCad design schematic/cells/sheets/level_attenuator.kicad_sch (2026-09-30)

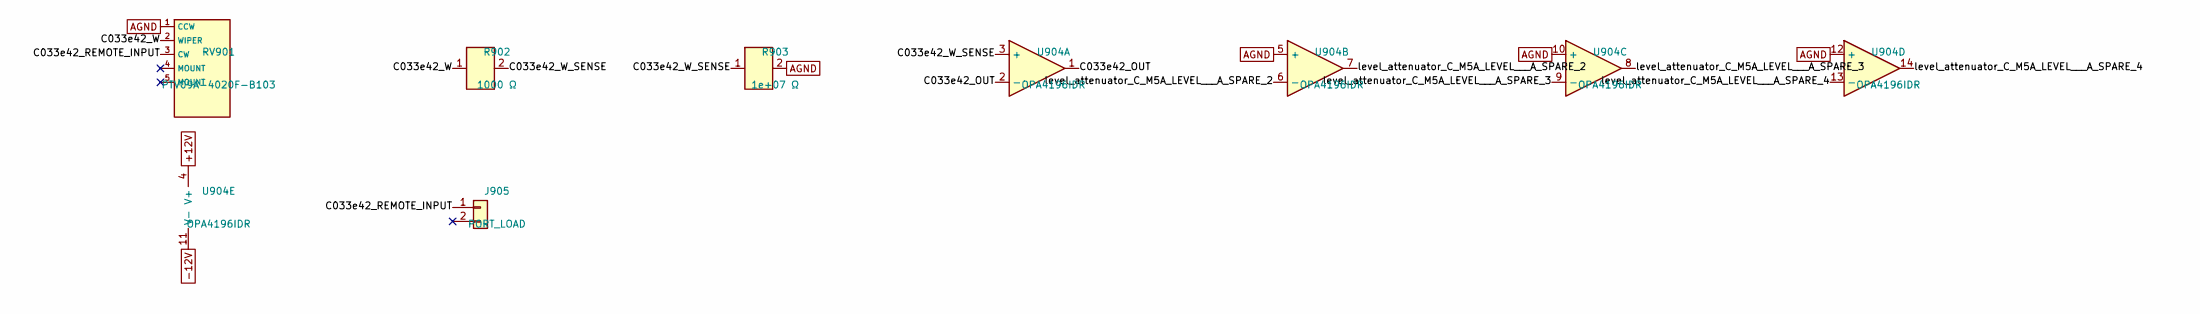
[picture p207: schematic level_attenuator.kicad_sch]

Parts:
J905: PORT_LOAD
R902: 1000 Ω; R0603
R903: 1e+07 Ω; R0603
RV901: PTV09A-4020F-B103; PTV09A-4020F; MPN PTV09A-4020F-B103; LCSC C5848782
U904: OPA4196IDR; SOIC-14_3.9x8.7mm_P1.27mm; MPN OPA4196IDR; LCSC C2057385

Connections:
+12V: U904.4 (V+)
-12V: U904.11 (V-)
AGND: R903.2, RV901.1 (CCW), U904.5 (+), U904.10 (+), U904.12 (+)
C033e42_OUT: U904.1, U904.2 (-)
C033e42_REMOTE_INPUT: J905.1, RV901.3 (CW)
C033e42_W: R902.1, RV901.2 (WIPER)
C033e42_W_SENSE: R902.2, R903.1, U904.3 (+)
level_attenuator_C_M5A_LEVEL___A_SPARE_2: U904.6 (-), U904.7
level_attenuator_C_M5A_LEVEL___A_SPARE_3: U904.8, U904.9 (-)
level_attenuator_C_M5A_LEVEL___A_SPARE_4: U904.13 (-), U904.14
