Takazudo/zudo-osc-hole-field/schematic/cells/sheets/magnitude_indicator.kicad_sch

## KiCad design schematic/cells/sheets/magnitude_indicator.kicad_sch (2026-09-30)

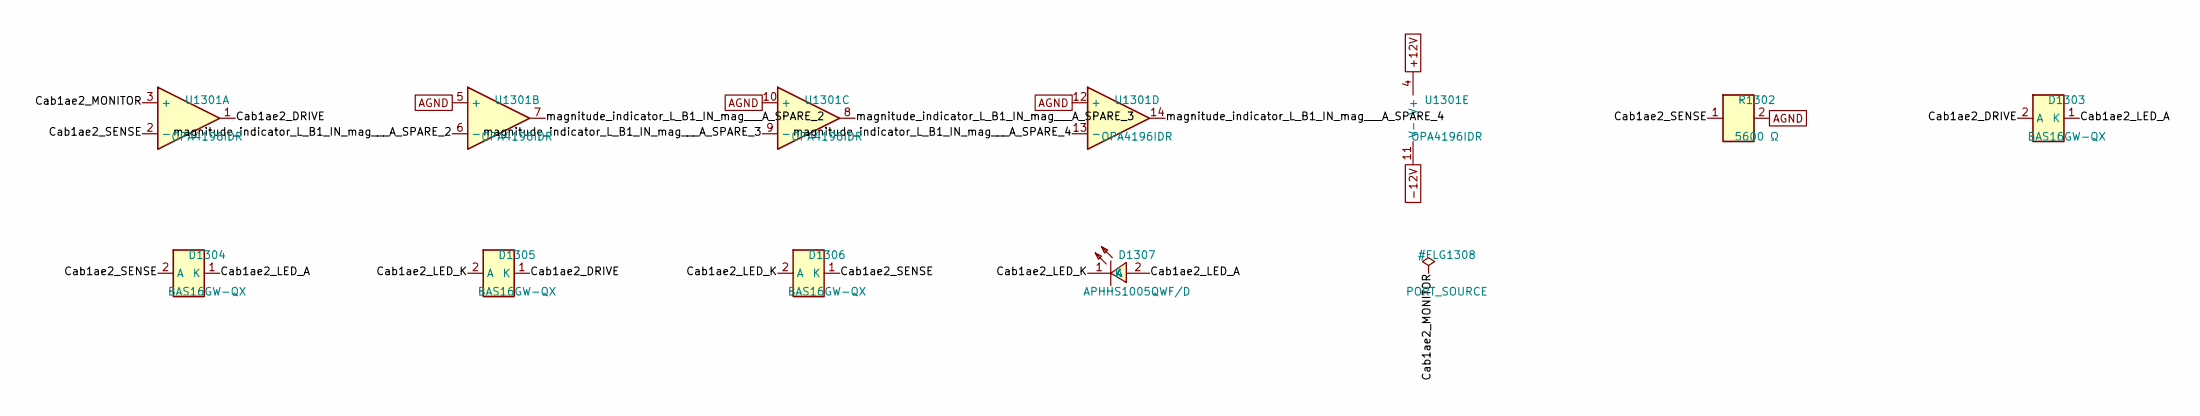
[picture p208: schematic magnitude_indicator.kicad_sch]

Parts:
D1303, D1304, D1305, D1306: BAS16GW-QX; SOD-123; MPN BAS16GW-QX
D1307: APHHS1005QWF/D; LED0402-Kingbright-White; MPN APHHS1005QWF/D
R1302: 5600 Ω; R0603
U1301: OPA4196IDR; SOIC-14_3.9x8.7mm_P1.27mm; MPN OPA4196IDR; LCSC C2057385

Connections:
+12V: U1301.4 (V+)
-12V: U1301.11 (V-)
AGND: R1302.2, U1301.5 (+), U1301.10 (+), U1301.12 (+)
Cab1ae2_DRIVE: D1303.2 (A), D1305.1 (K), U1301.1
Cab1ae2_LED_A: D1303.1 (K), D1304.1 (K), D1307.2 (A)
Cab1ae2_LED_K: D1305.2 (A), D1306.2 (A), D1307.1 (K)
Cab1ae2_MONITOR: U1301.3 (+)
Cab1ae2_SENSE: D1304.2 (A), D1306.1 (K), R1302.1, U1301.2 (-)
magnitude_indicator_L_B1_IN_mag___A_SPARE_2: U1301.6 (-), U1301.7
magnitude_indicator_L_B1_IN_mag___A_SPARE_3: U1301.8, U1301.9 (-)
magnitude_indicator_L_B1_IN_mag___A_SPARE_4: U1301.13 (-), U1301.14
