Takazudo/zudo-osc-hole-field/schematic/cells/sheets/octave_reference.kicad_sch

## KiCad design schematic/cells/sheets/octave_reference.kicad_sch (2026-09-30)

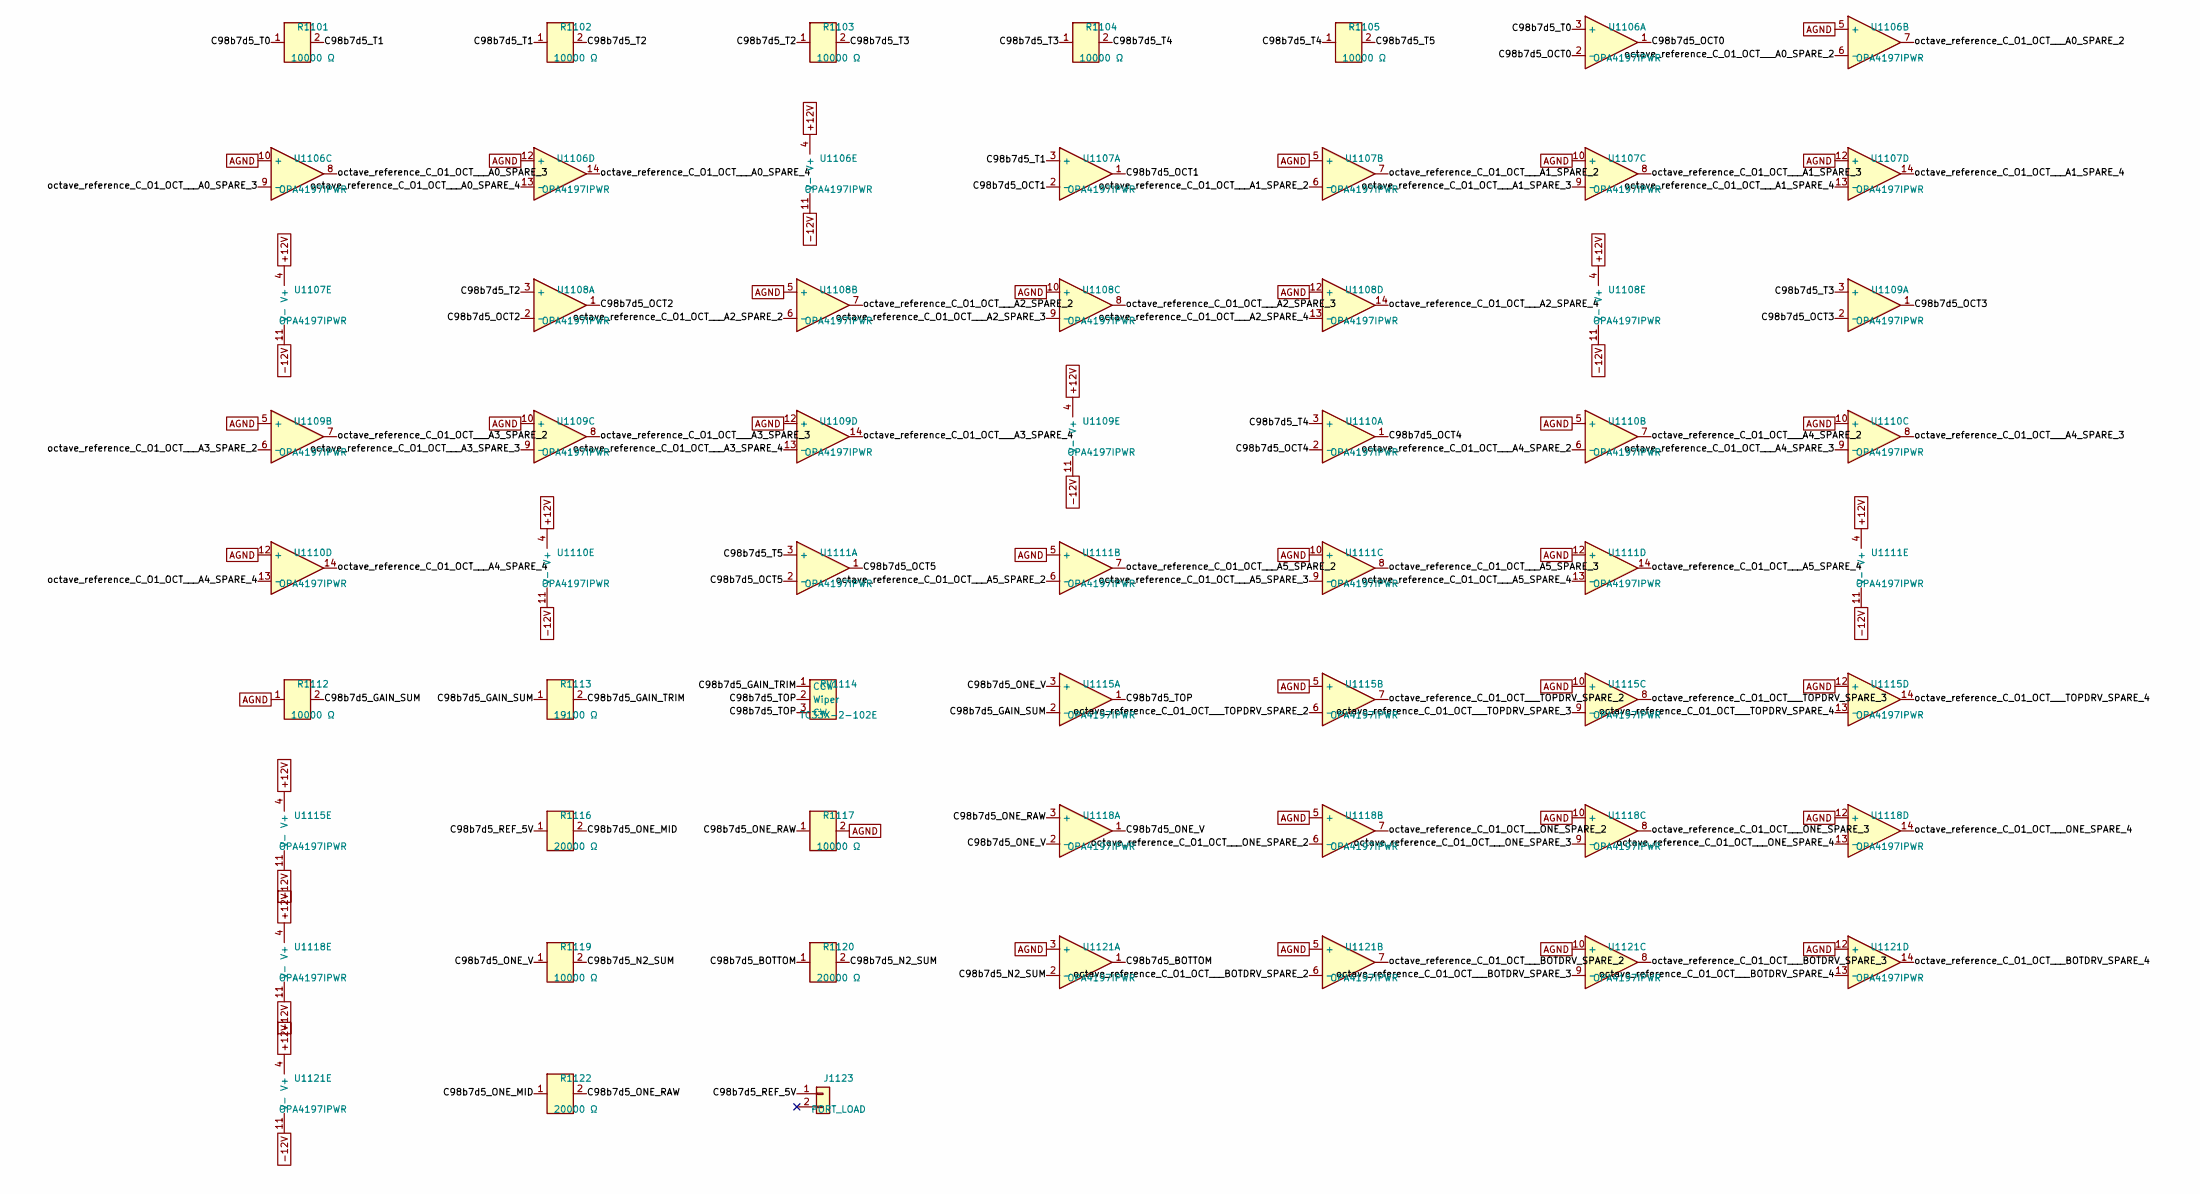
[picture p209: schematic octave_reference.kicad_sch]

Parts:
J1123: PORT_LOAD
R1101, R1102, R1103, R1104, R1105, R1112, R1117, R1119: 10000 Ω; R0603
R1113: 19100 Ω; R0603
R1116, R1120, R1122: 20000 Ω; R0603
RV1114: TC33X-2-102E; Potentiometer_Bourns_TC33X_Vertical; MPN TC33X-2-102E
U1106, U1107, U1108, U1109, U1110, U1111, U1115, U1118, U1121: OPA4197IPWR; TSSOP-14_4.4x5mm_P0.65mm; MPN OPA4197IPWR; LCSC C2057327

Connections:
+12V: U1106.4 (V+), U1107.4 (V+), U1108.4 (V+), U1109.4 (V+), U1110.4 (V+), U1111.4 (V+), U1115.4 (V+), U1118.4 (V+), U1121.4 (V+)
-12V: U1106.11 (V-), U1107.11 (V-), U1108.11 (V-), U1109.11 (V-), U1110.11 (V-), U1111.11 (V-), U1115.11 (V-), U1118.11 (V-), U1121.11 (V-)
AGND: R1112.1, R1117.2, U1106.5 (+), U1106.10 (+), U1106.12 (+), U1107.5 (+), U1107.10 (+), U1107.12 (+), U1108.5 (+), U1108.10 (+), U1108.12 (+), U1109.5 (+), U1109.10 (+), U1109.12 (+), U1110.5 (+), U1110.10 (+), U1110.12 (+), U1111.5 (+), U1111.10 (+), U1111.12 (+), U1115.5 (+), U1115.10 (+), U1115.12 (+), U1118.5 (+), U1118.10 (+), U1118.12 (+), U1121.3 (+), U1121.5 (+), U1121.10 (+), U1121.12 (+)
C98b7d5_BOTTOM: R1120.1, U1121.1
C98b7d5_GAIN_SUM: R1112.2, R1113.1, U1115.2 (-)
C98b7d5_GAIN_TRIM: R1113.2, RV1114.1 (CCW)
C98b7d5_N2_SUM: R1119.2, R1120.2, U1121.2 (-)
C98b7d5_OCT0: U1106.1, U1106.2 (-)
C98b7d5_OCT1: U1107.1, U1107.2 (-)
C98b7d5_OCT2: U1108.1, U1108.2 (-)
C98b7d5_OCT3: U1109.1, U1109.2 (-)
C98b7d5_OCT4: U1110.1, U1110.2 (-)
C98b7d5_OCT5: U1111.1, U1111.2 (-)
C98b7d5_ONE_MID: R1116.2, R1122.1
C98b7d5_ONE_RAW: R1117.1, R1122.2, U1118.3 (+)
C98b7d5_ONE_V: R1119.1, U1115.3 (+), U1118.1, U1118.2 (-)
C98b7d5_REF_5V: J1123.1, R1116.1
C98b7d5_T0: R1101.1, U1106.3 (+)
C98b7d5_T1: R1101.2, R1102.1, U1107.3 (+)
C98b7d5_T2: R1102.2, R1103.1, U1108.3 (+)
C98b7d5_T3: R1103.2, R1104.1, U1109.3 (+)
C98b7d5_T4: R1104.2, R1105.1, U1110.3 (+)
C98b7d5_T5: R1105.2, U1111.3 (+)
C98b7d5_TOP: RV1114.2 (Wiper), RV1114.3 (CW), U1115.1
octave_reference_C_O1_OCT___A0_SPARE_2: U1106.6 (-), U1106.7
octave_reference_C_O1_OCT___A0_SPARE_3: U1106.8, U1106.9 (-)
octave_reference_C_O1_OCT___A0_SPARE_4: U1106.13 (-), U1106.14
octave_reference_C_O1_OCT___A1_SPARE_2: U1107.6 (-), U1107.7
octave_reference_C_O1_OCT___A1_SPARE_3: U1107.8, U1107.9 (-)
octave_reference_C_O1_OCT___A1_SPARE_4: U1107.13 (-), U1107.14
octave_reference_C_O1_OCT___A2_SPARE_2: U1108.6 (-), U1108.7
octave_reference_C_O1_OCT___A2_SPARE_3: U1108.8, U1108.9 (-)
octave_reference_C_O1_OCT___A2_SPARE_4: U1108.13 (-), U1108.14
octave_reference_C_O1_OCT___A3_SPARE_2: U1109.6 (-), U1109.7
octave_reference_C_O1_OCT___A3_SPARE_3: U1109.8, U1109.9 (-)
octave_reference_C_O1_OCT___A3_SPARE_4: U1109.13 (-), U1109.14
octave_reference_C_O1_OCT___A4_SPARE_2: U1110.6 (-), U1110.7
octave_reference_C_O1_OCT___A4_SPARE_3: U1110.8, U1110.9 (-)
octave_reference_C_O1_OCT___A4_SPARE_4: U1110.13 (-), U1110.14
octave_reference_C_O1_OCT___A5_SPARE_2: U1111.6 (-), U1111.7
octave_reference_C_O1_OCT___A5_SPARE_3: U1111.8, U1111.9 (-)
octave_reference_C_O1_OCT___A5_SPARE_4: U1111.13 (-), U1111.14
octave_reference_C_O1_OCT___BOTDRV_SPARE_2: U1121.6 (-), U1121.7
octave_reference_C_O1_OCT___BOTDRV_SPARE_3: U1121.8, U1121.9 (-)
octave_reference_C_O1_OCT___BOTDRV_SPARE_4: U1121.13 (-), U1121.14
octave_reference_C_O1_OCT___ONE_SPARE_2: U1118.6 (-), U1118.7
octave_reference_C_O1_OCT___ONE_SPARE_3: U1118.8, U1118.9 (-)
octave_reference_C_O1_OCT___ONE_SPARE_4: U1118.13 (-), U1118.14
octave_reference_C_O1_OCT___TOPDRV_SPARE_2: U1115.6 (-), U1115.7
octave_reference_C_O1_OCT___TOPDRV_SPARE_3: U1115.8, U1115.9 (-)
octave_reference_C_O1_OCT___TOPDRV_SPARE_4: U1115.13 (-), U1115.14
