Takazudo/zudo-osc-hole-field/schematic/cells/sheets/precision_output.kicad_sch

## KiCad design schematic/cells/sheets/precision_output.kicad_sch (2026-10-02)

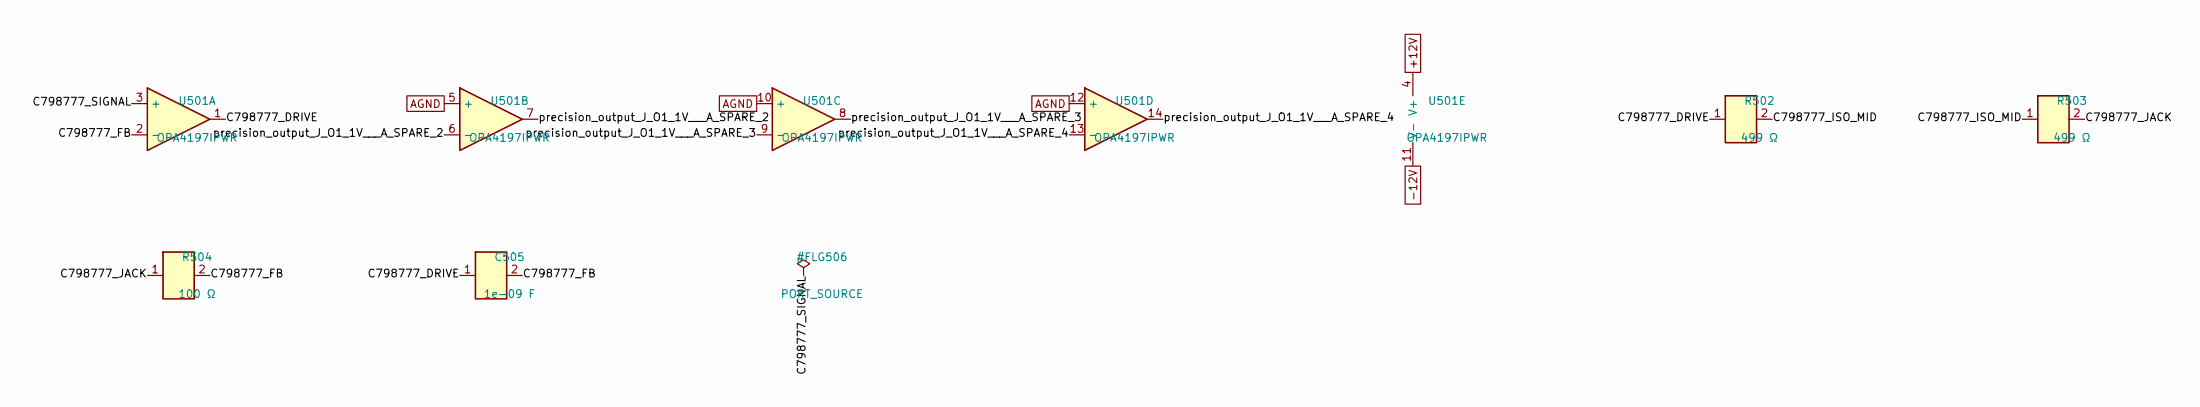
[picture p210: schematic precision_output.kicad_sch]

Parts:
C505: 1e-09 F; C0603; MPN C0603C102J5GACTU
R502, R503: 499 Ω; R_1210_3225Metric; MPN RC1210FR-07499RL
R504: 100 Ω; R0603; MPN RC0603FR-07100RL
U501: OPA4197IPWR; TSSOP-14_4.4x5mm_P0.65mm; MPN OPA4197IPWR; LCSC C2057327

Connections:
+12V: U501.4 (V+)
-12V: U501.11 (V-)
AGND: U501.5 (+), U501.10 (+), U501.12 (+)
C798777_DRIVE: C505.1, R502.1, U501.1
C798777_FB: C505.2, R504.2, U501.2 (-)
C798777_ISO_MID: R502.2, R503.1
C798777_JACK: R503.2, R504.1
C798777_SIGNAL: U501.3 (+)
precision_output_J_O1_1V___A_SPARE_2: U501.6 (-), U501.7
precision_output_J_O1_1V___A_SPARE_3: U501.8, U501.9 (-)
precision_output_J_O1_1V___A_SPARE_4: U501.13 (-), U501.14
