Takazudo/zudo-osc-hole-field/schematic/cells/sheets/reference_generator.kicad_sch

## KiCad design schematic/cells/sheets/reference_generator.kicad_sch (2026-09-30)

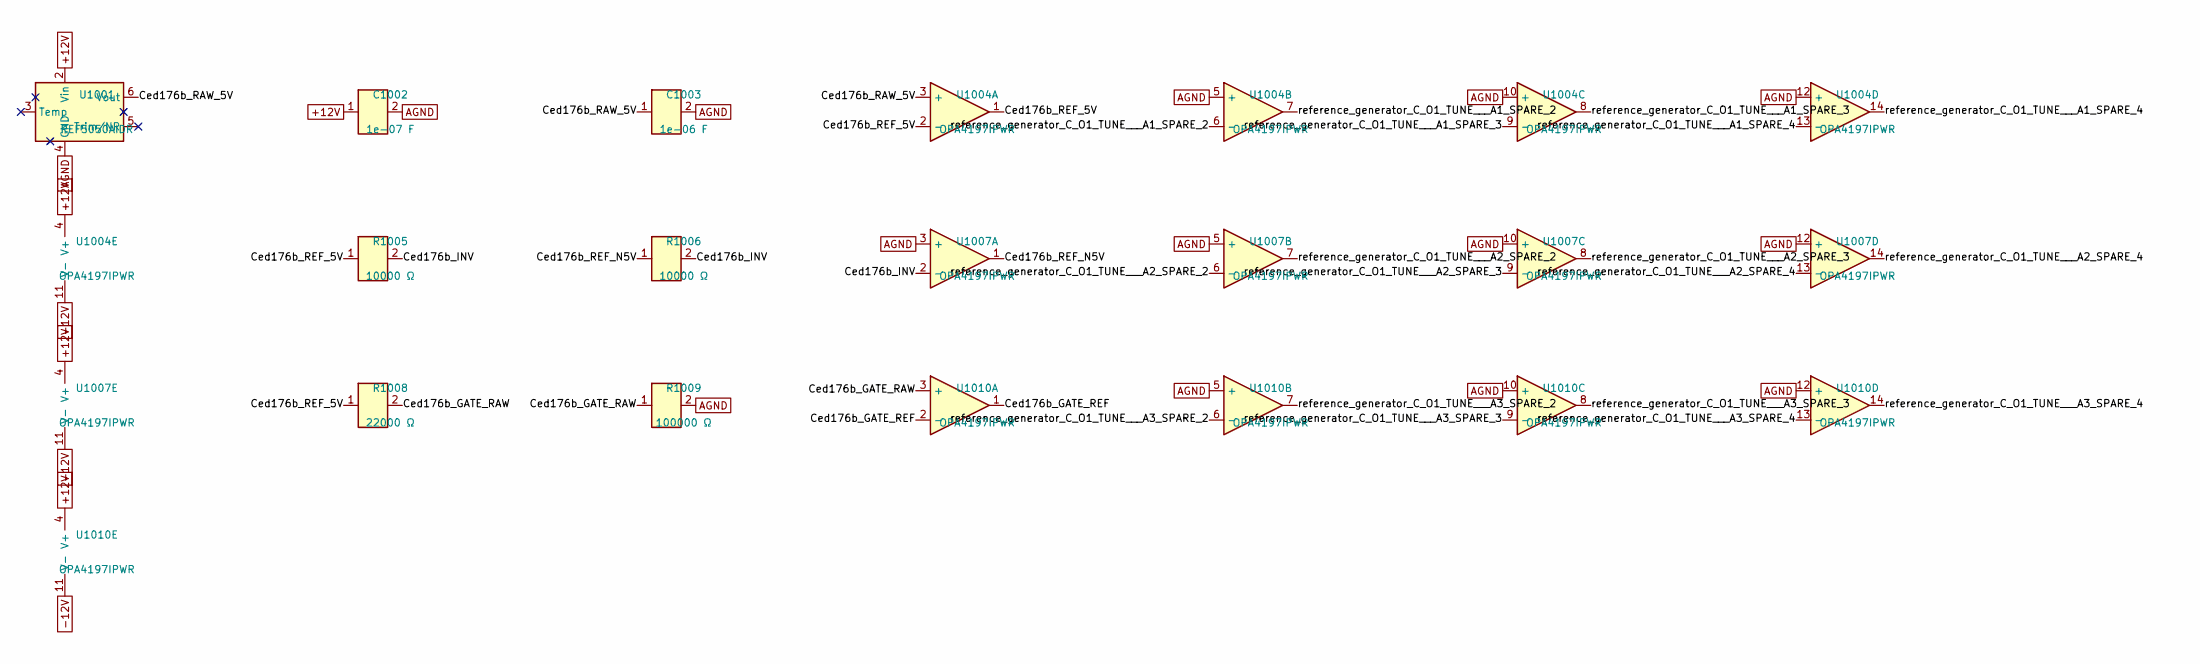
[picture p211: schematic reference_generator.kicad_sch]

Parts:
C1002: 1e-07 F; C0603; MPN GRM188R71H104KA93D
C1003: 1e-06 F; C0603
R1005, R1006: 10000 Ω; R0603
R1008: 22000 Ω; R0603
R1009: 100000 Ω; R0603; MPN RT0603BRD07100KL
U1001: REF5050AIDR; SOIC-8_3.9x4.9mm_P1.27mm; MPN REF5050AIDR; LCSC C27804
U1004, U1007, U1010: OPA4197IPWR; TSSOP-14_4.4x5mm_P0.65mm; MPN OPA4197IPWR; LCSC C2057327

Connections:
+12V: C1002.1, U1001.2 (Vin), U1004.4 (V+), U1007.4 (V+), U1010.4 (V+)
-12V: U1004.11 (V-), U1007.11 (V-), U1010.11 (V-)
AGND: C1002.2, C1003.2, R1009.2, U1001.4 (GND), U1004.5 (+), U1004.10 (+), U1004.12 (+), U1007.3 (+), U1007.5 (+), U1007.10 (+), U1007.12 (+), U1010.5 (+), U1010.10 (+), U1010.12 (+)
Ced176b_GATE_RAW: R1008.2, R1009.1, U1010.3 (+)
Ced176b_GATE_REF: U1010.1, U1010.2 (-)
Ced176b_INV: R1005.2, R1006.2, U1007.2 (-)
Ced176b_RAW_5V: C1003.1, U1001.6 (Vout), U1004.3 (+)
Ced176b_REF_5V: R1005.1, R1008.1, U1004.1, U1004.2 (-)
Ced176b_REF_N5V: R1006.1, U1007.1
reference_generator_C_O1_TUNE___A1_SPARE_2: U1004.6 (-), U1004.7
reference_generator_C_O1_TUNE___A1_SPARE_3: U1004.8, U1004.9 (-)
reference_generator_C_O1_TUNE___A1_SPARE_4: U1004.13 (-), U1004.14
reference_generator_C_O1_TUNE___A2_SPARE_2: U1007.6 (-), U1007.7
reference_generator_C_O1_TUNE___A2_SPARE_3: U1007.8, U1007.9 (-)
reference_generator_C_O1_TUNE___A2_SPARE_4: U1007.13 (-), U1007.14
reference_generator_C_O1_TUNE___A3_SPARE_2: U1010.6 (-), U1010.7
reference_generator_C_O1_TUNE___A3_SPARE_3: U1010.8, U1010.9 (-)
reference_generator_C_O1_TUNE___A3_SPARE_4: U1010.13 (-), U1010.14
