Takazudo/zudo-osc-hole-field/schematic/cells/sheets/remote_buffer.kicad_sch

## KiCad design schematic/cells/sheets/remote_buffer.kicad_sch (2026-09-30)

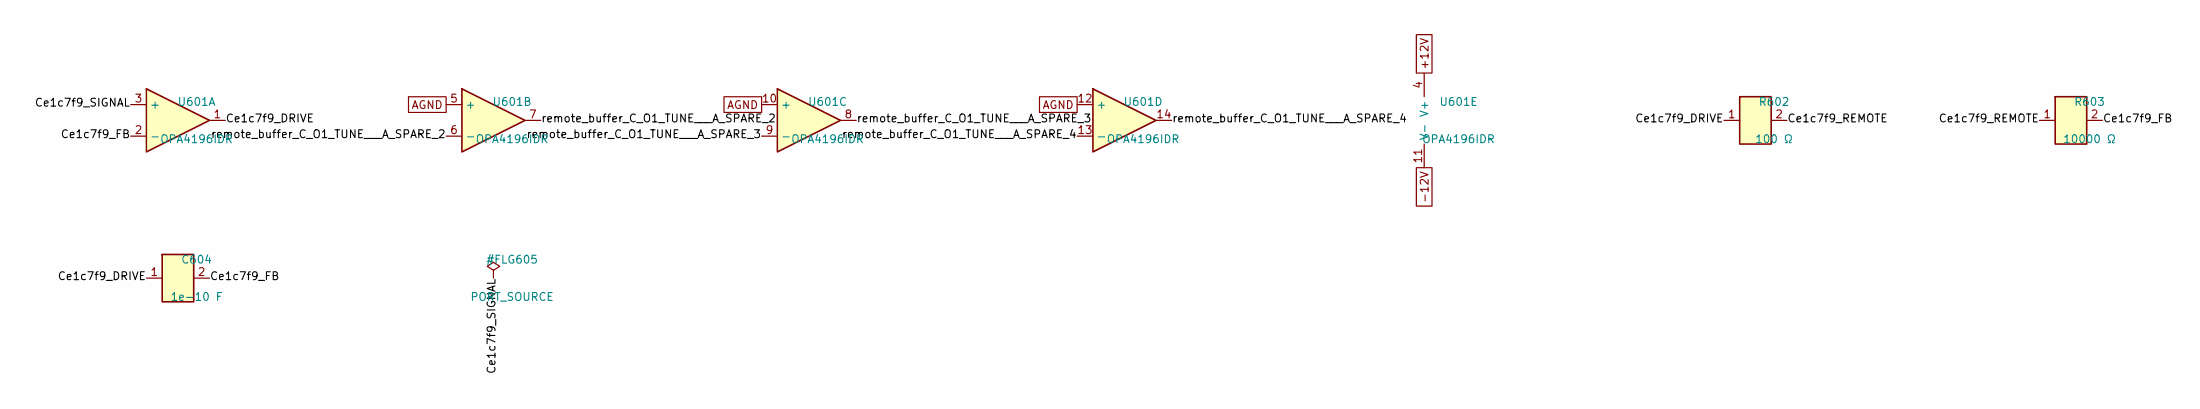
[picture p212: schematic remote_buffer.kicad_sch]

Parts:
C604: 1e-10 F; C0603; MPN C0603C101J5GACTU
R602: 100 Ω; R0603
R603: 10000 Ω; R0603
U601: OPA4196IDR; SOIC-14_3.9x8.7mm_P1.27mm; MPN OPA4196IDR; LCSC C2057385

Connections:
+12V: U601.4 (V+)
-12V: U601.11 (V-)
AGND: U601.5 (+), U601.10 (+), U601.12 (+)
Ce1c7f9_DRIVE: C604.1, R602.1, U601.1
Ce1c7f9_FB: C604.2, R603.2, U601.2 (-)
Ce1c7f9_REMOTE: R602.2, R603.1
Ce1c7f9_SIGNAL: U601.3 (+)
remote_buffer_C_O1_TUNE___A_SPARE_2: U601.6 (-), U601.7
remote_buffer_C_O1_TUNE___A_SPARE_3: U601.8, U601.9 (-)
remote_buffer_C_O1_TUNE___A_SPARE_4: U601.13 (-), U601.14
