Takazudo/zudo-osc-hole-field/schematic/cells/sheets/slew_island.kicad_sch

## KiCad design schematic/cells/sheets/slew_island.kicad_sch (2026-09-30)

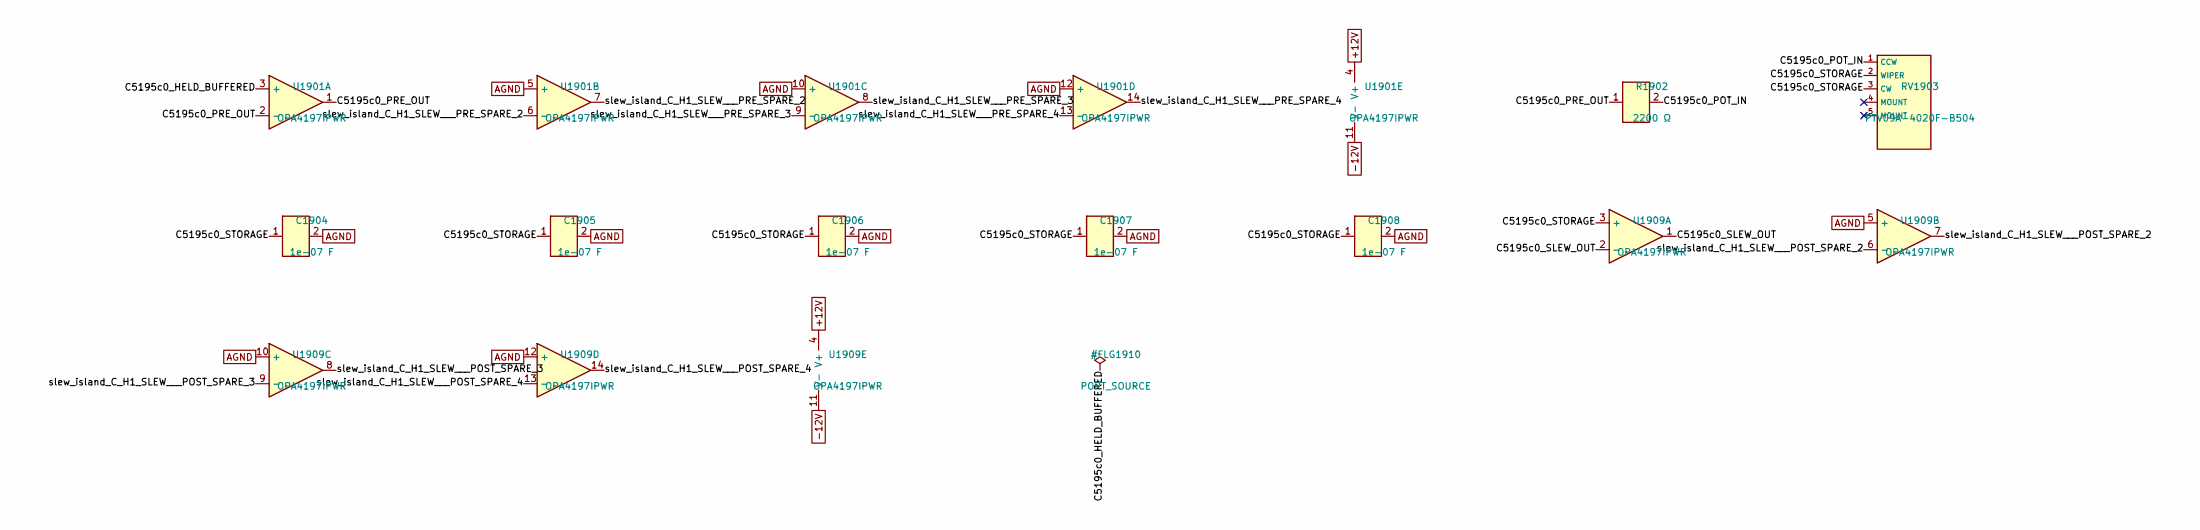
[picture p213: schematic slew_island.kicad_sch]

Parts:
C1904, C1905, C1906, C1907, C1908: 1e-07 F; C1206; MPN 1206CG104J500NT; LCSC C46348
R1902: 2200 Ω; R0603
RV1903: PTV09A-4020F-B504; PTV09A-4020F; MPN PTV09A-4020F-B504; LCSC C5154140
U1901, U1909: OPA4197IPWR; TSSOP-14_4.4x5mm_P0.65mm; MPN OPA4197IPWR; LCSC C2057327

Connections:
+12V: U1901.4 (V+), U1909.4 (V+)
-12V: U1901.11 (V-), U1909.11 (V-)
AGND: C1904.2, C1905.2, C1906.2, C1907.2, C1908.2, U1901.5 (+), U1901.10 (+), U1901.12 (+), U1909.5 (+), U1909.10 (+), U1909.12 (+)
C5195c0_HELD_BUFFERED: U1901.3 (+)
C5195c0_POT_IN: R1902.2, RV1903.1 (CCW)
C5195c0_PRE_OUT: R1902.1, U1901.1, U1901.2 (-)
C5195c0_SLEW_OUT: U1909.1, U1909.2 (-)
C5195c0_STORAGE: C1904.1, C1905.1, C1906.1, C1907.1, C1908.1, RV1903.2 (WIPER), RV1903.3 (CW), U1909.3 (+)
slew_island_C_H1_SLEW___POST_SPARE_2: U1909.6 (-), U1909.7
slew_island_C_H1_SLEW___POST_SPARE_3: U1909.8, U1909.9 (-)
slew_island_C_H1_SLEW___POST_SPARE_4: U1909.13 (-), U1909.14
slew_island_C_H1_SLEW___PRE_SPARE_2: U1901.6 (-), U1901.7
slew_island_C_H1_SLEW___PRE_SPARE_3: U1901.8, U1901.9 (-)
slew_island_C_H1_SLEW___PRE_SPARE_4: U1901.13 (-), U1901.14
