Takazudo/zudo-osc-hole-field/schematic/cells/sheets/stage_indicator.kicad_sch

## KiCad design schematic/cells/sheets/stage_indicator.kicad_sch (2026-09-30)

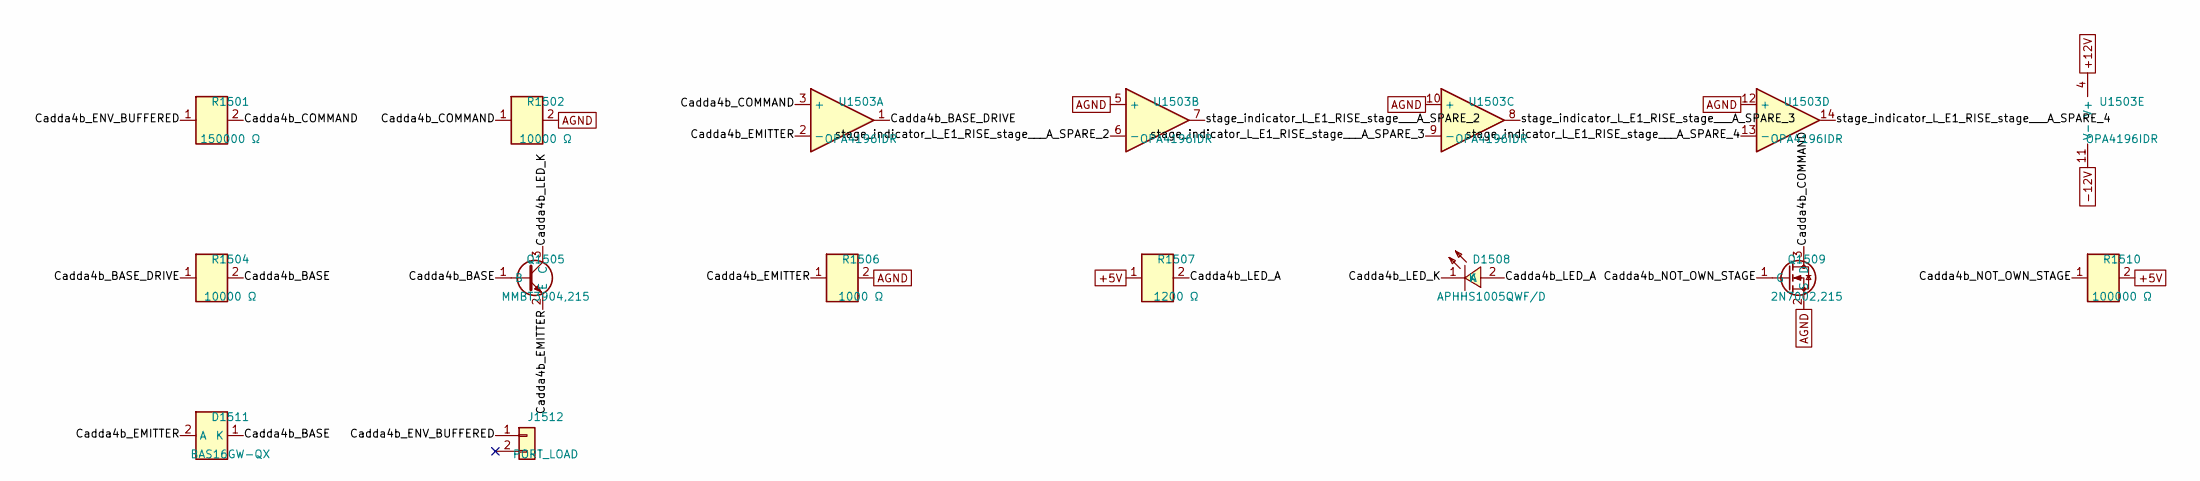
[picture p214: schematic stage_indicator.kicad_sch]

Parts:
D1508: APHHS1005QWF/D; LED0402-Kingbright-White; MPN APHHS1005QWF/D
D1511: BAS16GW-QX; SOD-123; MPN BAS16GW-QX
J1512: PORT_LOAD
Q1505: MMBT3904,215; SOT-23; MPN MMBT3904,215
Q1509: 2N7002,215; SOT-23; MPN 2N7002,215
R1501: 150000 Ω; R0603
R1502, R1504: 10000 Ω; R0603
R1506: 1000 Ω; R0603
R1507: 1200 Ω; R0603
R1510: 100000 Ω; R0603; MPN RC0603FR-07100KL
U1503: OPA4196IDR; SOIC-14_3.9x8.7mm_P1.27mm; MPN OPA4196IDR; LCSC C2057385

Connections:
+5V: R1507.1, R1510.2
+12V: U1503.4 (V+)
-12V: U1503.11 (V-)
AGND: Q1509.2 (S), R1502.2, R1506.2, U1503.5 (+), U1503.10 (+), U1503.12 (+)
Cadda4b_BASE: D1511.1 (K), Q1505.1 (B), R1504.2
Cadda4b_BASE_DRIVE: R1504.1, U1503.1
Cadda4b_COMMAND: Q1509.3 (D), R1501.2, R1502.1, U1503.3 (+)
Cadda4b_EMITTER: D1511.2 (A), Q1505.2 (E), R1506.1, U1503.2 (-)
Cadda4b_ENV_BUFFERED: J1512.1, R1501.1
Cadda4b_LED_A: D1508.2 (A), R1507.2
Cadda4b_LED_K: D1508.1 (K), Q1505.3 (C)
Cadda4b_NOT_OWN_STAGE: Q1509.1 (G), R1510.1
stage_indicator_L_E1_RISE_stage___A_SPARE_2: U1503.6 (-), U1503.7
stage_indicator_L_E1_RISE_stage___A_SPARE_3: U1503.8, U1503.9 (-)
stage_indicator_L_E1_RISE_stage___A_SPARE_4: U1503.13 (-), U1503.14
