Takazudo/zudo-osc-hole-field/schematic/cells/sheets/summing_node_input.kicad_sch

## KiCad design schematic/cells/sheets/summing_node_input.kicad_sch (2026-09-30)

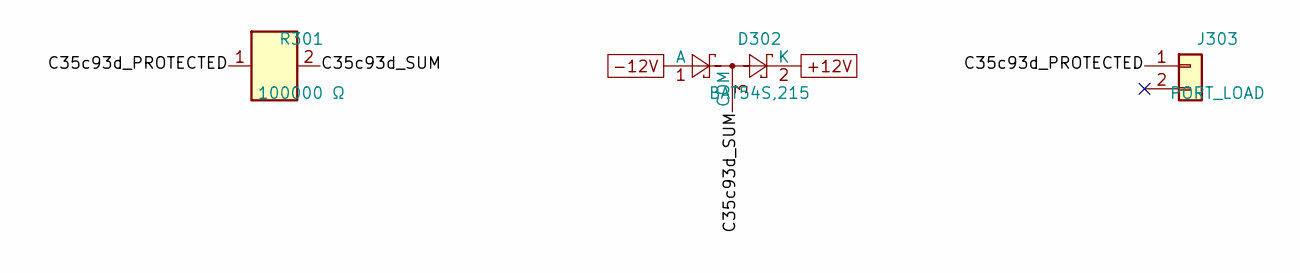
[picture p215: schematic summing_node_input.kicad_sch]

Parts:
D302: BAT54S,215; SOT-23; MPN BAT54S,215
J303: PORT_LOAD
R301: 100000 Ω; R0603; MPN RT0603BRD07100KL

Connections:
+12V: D302.2 (K)
-12V: D302.1 (A)
C35c93d_PROTECTED: J303.1, R301.1
C35c93d_SUM: D302.3 (COM), R301.2
