Takazudo/zudo-osc-hole-field/schematic/cells/sheets/switch_button_input.kicad_sch

## KiCad design schematic/cells/sheets/switch_button_input.kicad_sch (2026-09-30)

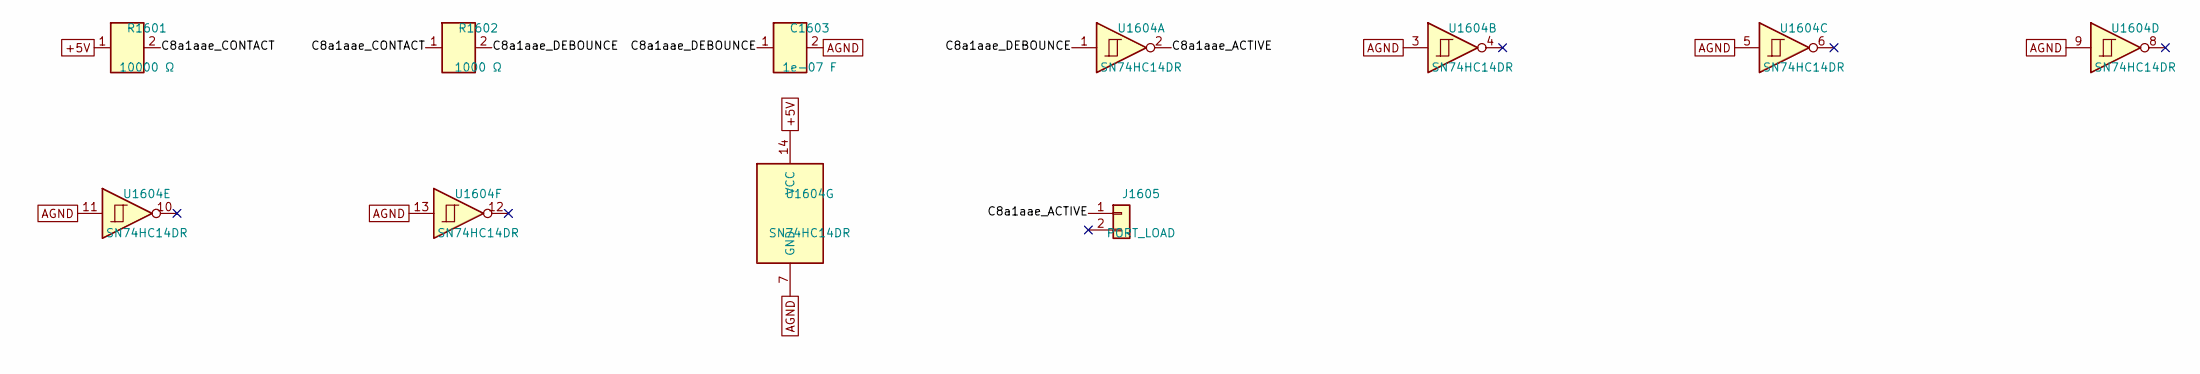
[picture p216: schematic switch_button_input.kicad_sch]

Parts:
C1603: 1e-07 F; C0603; MPN GRM188R71H104KA93D
J1605: PORT_LOAD
R1601: 10000 Ω; R0603
R1602: 1000 Ω; R0603
U1604: SN74HC14DR; SOIC-14_3.9x8.7mm_P1.27mm; MPN SN74HC14DR

Connections:
+5V: R1601.1, U1604.14 (VCC)
AGND: C1603.2, U1604.3, U1604.5, U1604.7 (GND), U1604.9, U1604.11, U1604.13
C8a1aae_ACTIVE: J1605.1, U1604.2
C8a1aae_CONTACT: R1601.2, R1602.1
C8a1aae_DEBOUNCE: C1603.1, R1602.2, U1604.1
