Takazudo/zudo-osc-hole-field/schematic/cells/sheets/trimmer.kicad_sch

## KiCad design schematic/cells/sheets/trimmer.kicad_sch (2026-09-30)

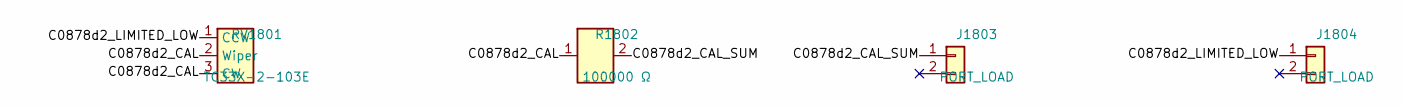
[picture p217: schematic trimmer.kicad_sch]

Parts:
J1803, J1804: PORT_LOAD
R1802: 100000 Ω; R0603; MPN RT0603BRD07100KL
RV1801: TC33X-2-103E; Potentiometer_Bourns_TC33X_Vertical; MPN TC33X-2-103E

Connections:
C0878d2_CAL: R1802.1, RV1801.2 (Wiper), RV1801.3 (CW)
C0878d2_CAL_SUM: J1803.1, R1802.2
C0878d2_LIMITED_LOW: J1804.1, RV1801.1 (CCW)
