Takazudo/zudo-osc-hole-field/schematic/candidates/monitor-permit/sheets/MonitorPermit-p2.kicad_sch

## KiCad design schematic/candidates/monitor-permit/sheets/MonitorPermit-p2.kicad_sch (2026-10-02)

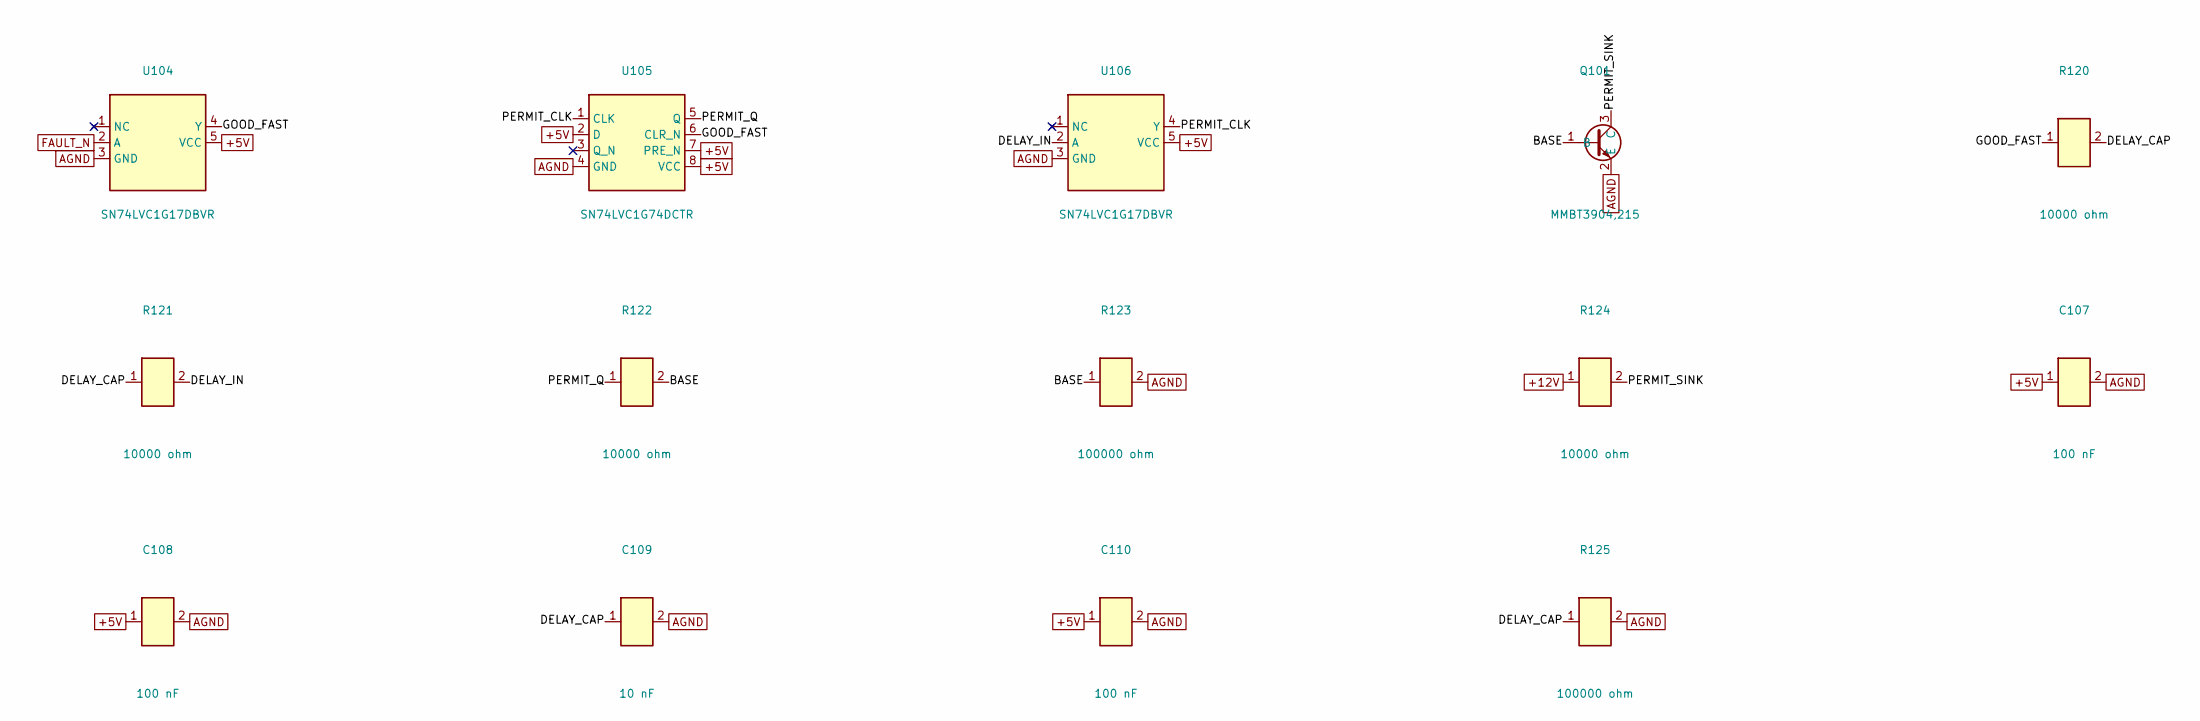
[picture p218: schematic MonitorPermit-p2.kicad_sch]

Parts:
C107, C108, C110: 100 nF; KEMET_C0603_DensityB; MPN C0603C104K5RACTU
C109: 10 nF; C0805; MPN C0805C103J5GACTU
Q101: MMBT3904,215; SOT-23; MPN MMBT3904,215
R120, R121, R122, R124: 10000 ohm; R_0805_2012Metric_Monitor; MPN RC0805FR-0710KL
R123, R125: 100000 ohm; R_0805_2012Metric_Monitor; MPN RC0805FR-07100KL
U104, U106: SN74LVC1G17DBVR; SOT-23-5; MPN SN74LVC1G17DBVR
U105: SN74LVC1G74DCTR; TI_DCT0008A; MPN SN74LVC1G74DCTR

Connections:
+5V: C107.1, C108.1, C110.1, U104.5 (VCC), U105.2 (D), U105.7 (PRE_N), U105.8 (VCC), U106.5 (VCC)
+12V: R124.1
AGND: C107.2, C108.2, C109.2, C110.2, Q101.2 (E), R123.2, R125.2, U104.3 (GND), U105.4 (GND), U106.3 (GND)
BASE: Q101.1 (B), R122.2, R123.1
DELAY_CAP: C109.1, R120.2, R121.1, R125.1
DELAY_IN: R121.2, U106.2 (A)
FAULT_N: U104.2 (A)
GOOD_FAST: R120.1, U104.4 (Y), U105.6 (CLR_N)
PERMIT_CLK: U105.1 (CLK), U106.4 (Y)
PERMIT_Q: R122.1, U105.5 (Q)
PERMIT_SINK: Q101.3 (C), R124.2
