Takazudo/zudo-osc-hole-field/schematic/candidates/monitor-permit/sheets/MonitorPermit.kicad_sch

## KiCad design schematic/candidates/monitor-permit/sheets/MonitorPermit.kicad_sch (2026-10-02)

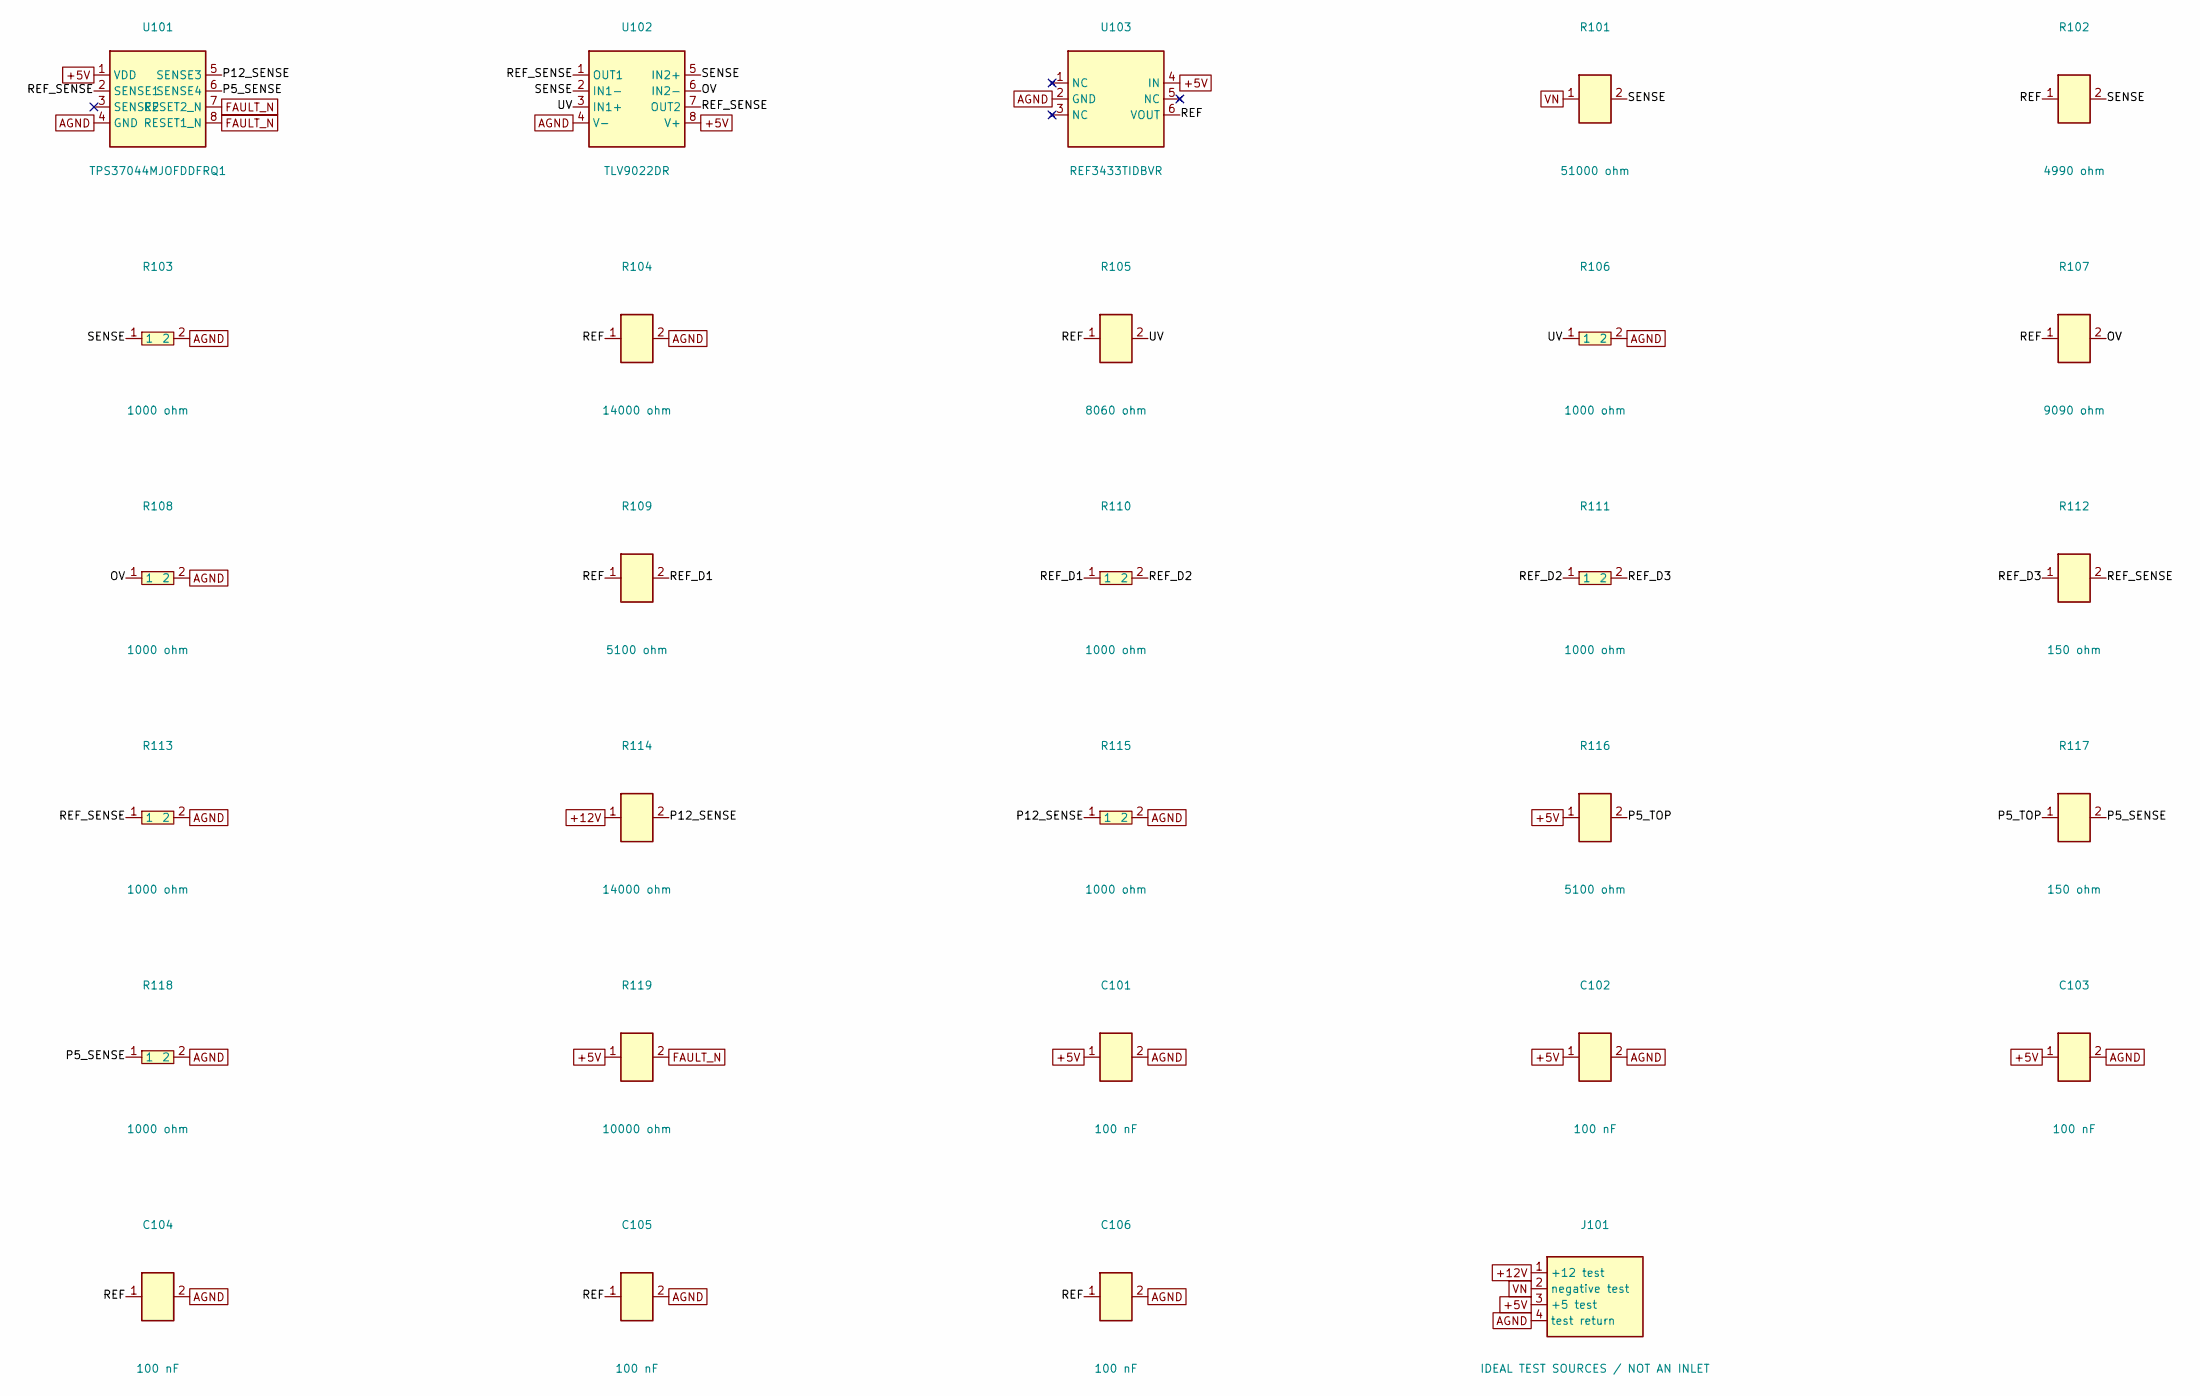
[picture p219: schematic MonitorPermit.kicad_sch]

Parts:
C101, C102, C103: 100 nF; KEMET_C0603_DensityB; MPN C0603C104K5RACTU
C104, C105, C106: 100 nF; KEMET_C1206_C0G_DensityB; MPN C1206C104F3GACTU
J101: IDEAL TEST SOURCES / NOT AN INLET
R101: 51000 ohm; R0603; MPN RT0603BRD0751KL
R102: 4990 ohm; R0603; MPN RT0603BRD074K99L
R103, R106, R108, R110, R111, R113, R115, R118: 1000 ohm; R0603; MPN RT0603BRD071KL
R104, R114: 14000 ohm; R0603; MPN RT0603BRD0714KL
R105: 8060 ohm; R0603; MPN RT0603BRD078K06L
R107: 9090 ohm; R0603; MPN RT0603BRD079K09L
R109, R116: 5100 ohm; R0603; MPN RT0603BRD075K1L
R112, R117: 150 ohm; R0603; MPN RT0603BRD07150RL
R119: 10000 ohm; R_0805_2012Metric_Monitor; MPN RC0805FR-0710KL
U101: TPS37044MJOFDDFRQ1; SOT-23-8; MPN TPS37044MJOFDDFRQ1
U102: TLV9022DR; SOIC-8_3.9x4.9mm_P1.27mm; MPN TLV9022DR
U103: REF3433TIDBVR; SOT-23-6; MPN REF3433TIDBVR

Connections:
+5V: C101.1, C102.1, C103.1, J101.3 (+5 test), R116.1, R119.1, U101.1 (VDD), U102.8 (V+), U103.4 (IN)
+12V: J101.1 (+12 test), R114.1
AGND: C101.2, C102.2, C103.2, C104.2, C105.2, C106.2, J101.4 (test return), R103.2, R104.2, R106.2, R108.2, R113.2, R115.2, R118.2, U101.4 (GND), U102.4 (V-), U103.2 (GND)
FAULT_N: R119.2, U101.7 (RESET2_N), U101.8 (RESET1_N)
OV: R107.2, R108.1, U102.6 (IN2-)
P5_SENSE: R117.2, R118.1, U101.6 (SENSE4)
P5_TOP: R116.2, R117.1
P12_SENSE: R114.2, R115.1, U101.5 (SENSE3)
REF: C104.1, C105.1, C106.1, R102.1, R104.1, R105.1, R107.1, R109.1, U103.6 (VOUT)
REF_D1: R109.2, R110.1
REF_D2: R110.2, R111.1
REF_D3: R111.2, R112.1
REF_SENSE: R112.2, R113.1, U101.2 (SENSE1), U102.1 (OUT1), U102.7 (OUT2)
SENSE: R101.2, R102.2, R103.1, U102.2 (IN1-), U102.5 (IN2+)
UV: R105.2, R106.1, U102.3 (IN1+)
VN: J101.2 (negative test), R101.1
